meshsat/meshsat-fieldkit/v2/docs/records/README.md

# Session records cited by the committed pages

MESHSAT-1357, filed 26 September 2026 (stream `records`, from main `45bde541`). The MeshSat field kit V2 is a prototype design: no board of the set has been built, and nothing in this folder has been measured on hardware.

## What this folder is

The foundation session of 25 and 26 September 2026 worked in git worktrees, one per stream (branches `fnd/<name>`), and kept its working files in each worktree's untracked `drafts/` folder: the scripts it ran, their outputs, the netlist readings, the decision logs of each board's author and the lists of documents it fetched. Committed pages cite those files, and no reader of the repository could open them. They are filed here so an outside reviewer can.

- **Layout.** `v2/docs/records/<worktree>/<the same path below drafts/>`: `drafts/dec_loop.py` of worktree `fnd/rv-dec` is `rv-dec/dec_loop.py` here.
- **Records, not repository tools.** No test, gate or generator runs them. A script here keeps its original text, including paths into `drafts/` or onto the rented build box (`/root/...`) that only existed where it ran; the table below maps every such `drafts/` path to its place here.
- **Byte for byte**, with two exceptions: in `rv-dec/PCB-OPEN-PAIRS.decision-42.isolated.diff` and `r4b/box/r6-run6/check_pcb_b/emul-r6-gate-on-round6.txt` the absolute path of the session's scratch directory on the build host is replaced by `$SP` (the notation `MESHSAT-709-geometry-appendix.md` already uses for it). The table gives the filed sha256, and the section *Rewritten on filing* gives the worktree file's.
- **Not filed here** (sections below): maker documents, which belong in `v2/vendor/` with the parts stream; netlists and box run directories that are over 1 MB or that the repository's history already holds, each with its sha256 and the command that rebuilds it; third-party web page snapshots the battery packet chose not to publish. Nothing filed holds a credential or personal data; the only mail addresses in the folder are two companies' published functional ones (AsiaRF's sales address in `rv-pwr/pwr-maker-questions.md`, Jauch's battery-technology address quoted from its web page in `rv-bat/datasheets/SOURCES.txt`).
- **The session's choices in this filing** (taken by the session under the owner's standing rule of 26 September 2026): a file whose bytes the repository already holds is not filed twice, it is pointed to; a netlist that differs from a committed one only in its `(source ...)` and `(date ...)` header lines is rebuilt by a command whose output hash is checked here, not filed; the outputs of the scripts `DECOUPLING.md` section 11 cites are filed with them, because that page cites the scripts "and their outputs"; the two box scripts that `r4b/box/r6-run6/README.txt` names as the run's driver are filed with it.
- **A decision log is filed whole**, as its worktree held it when this was filed. `r4t/r4-decisions.md` is a snapshot of a file another loop was still editing (worktree file modified 20:50 CEST); see *Cited but not found*.

Worktrees:

| folder | whose records |
|---|---|
| `adj/` | the eleven adjudications A01 to A11 of 25 September (filed 27 September; section *Filed 27 September 2026*) |
| `handover/` | filed by the handover's H1.1 editor, 27 September 2026, so the handover pages' citations can be traced: hc4's two reviews and hc6's review, rendered from the session's workflow journal (AI reviews); the messages of commits `3a1f6576` (the parity report of 36 artefacts) and `a8652172` (the H1 filing, with the suite results); `3a1f6576-commit-message.txt` sha256 382d1771c084903b; `a8652172-commit-message.txt` sha256 15d4f2b04fd46883; `hc4-reviews.md` sha256 6941573f2b81298b; `hc6-review.md` sha256 3a72258e350d3ad7 Added 27 September 2026 by the integrating session: `H2-USABILITY-CHECK.md` (sha256 `b7e555783614defb1ce572a54786f11d6d93cc7ead7b52ec426557ddfd069fbe`), the fresh checker's full result on snapshot H2, filed verbatim from the workflow journal (AI usability check); `RELEASE-H2.md` in `v2/docs/handover/` cites it. |
| `hc2/` | the layer 2 closer hc2 (concept of operations, envelope and test plan) and its targeted fixer c23: the power and heat arithmetic the pages cite and the closer's hand-offs (filed at integration, 27 September 2026) |
| `hc3/` | the layer 3 closer hc3 (requirements registry) and its targeted fixer c23: the hand re-read of every carried citation, the list the apply script checks, the fixer's answer to each finding, and the layer's open questions and status row (filed at integration, 27 September 2026) |
| `hc4/` | the layer 4 closer hc4 (readable diagrams): the five disagreements between the energy chain and the netlists, for the energy chain's owner (filed at integration, 27 September 2026) |
| `hc7/` | the layer 7 closer hc7 (case fit and the case release) and its targeted fixer c7: board C's gate readings with and without the board reading, the fixer's answer and the landing notes (filed at integration, 27 September 2026) |
| `r4a/` | board A's author, rounds 4 to 6 (round-6 candidate, fix-ups 3 and 4) |
| `r4b/` | board B's author, rounds 4 to 6 (round-6 candidate, box run 6) |
| `r4e/` | board E's author, round 4 |
| `r4p/` | board P's author, round 4 |
| `r4t/` | the shared tools' author, rounds 4 to 7 (still being edited when this was filed) |
| `r6d/` | board D's author, round 6 |
| `r8b/` | board B's author, round 8 (the round's decision record, its tools, evidence and per-finding change list, and the decoupling classes; filed at integration, 27 September 2026, `drafts/b/X` at `r8b/X`); `r8b/integration/` holds the integration's own box procedure, comparator and logs |
| `r8d/` | board D's author, round 8 (the regeneration's independent comparison, gates and suite; filed at integration, 27 September 2026) |
| `r8int4/` | the integrator of set 4 of the handover (27 September 2026, branch `fnd/r8int4`): the scripts that merged the layer 2 and 3 closers, the re-take driver, the hardware-firmware contract and the case release onto main `38dcd764`, the hand re-reads they needed and the apply logs |
| `r8int5/` | the integrator of set 5 of the handover (27 September 2026, branch `fnd/r8int5`, on main `953f5658`): the shared helpers its per-stream scripts use (`edlib.py`, `render_group1.py`, `file_stream.py`; `file_records.py` is `r8int4/file_records.py` byte for byte and is not filed twice), the CURRENT-EVIDENCE rebind, the final regeneration of boards A, B, D and E on the KiCad box (`final-regen/`: every artefact PARITY or PARITY_AFTER_NOISE, the sidecars' generator identities unchanged) and its logs; each stream's own scripts are in its folder (`w3t/`, `w3a/`, `w3b/`, `w3de/`, `w3g/`); the session scratch path is written $SP in `file_stream.py`, `logs/diagrams-readback-b7f96784.log`, `logs/tests-w3de-targeted.log` |
| `r8int6/` | the integrator of set 6 of the handover (27 September 2026, branch `fnd/r8int6`, on main `6ec37197`): the shared scripts that applied streams w4r, w4b, w4c, w4ae and w4dp (`common/` and the drivers; each stream's own apply script is in its folder), the set 6 lines on the layer status page with the V2-SPEC correction and the open item they name (`layers_r8int6.py`), the CURRENT-EVIDENCE rebind, the final regeneration of boards A, B, C, D, E and P on the KiCad box at `932cf9d7` (`final-regen/`: every artefact PARITY or PARITY_AFTER_NOISE, no land moved, every sidecar's generator identity equal to the committed one, so no sidecar is re-stamped), the independent netlist comparison of each board against its stream's expected list (`indep/`), and the evidence phase's logs (`evidence-phase/`); the session scratch path is written $SP in `commit_r8int6.sh`, `common/file_stream_r8int6.py`, `copy_evidence.sh`, `evidence_r8int6.sh`, `indep/summary.txt`, `kitprep_r8int6.sh`, `stream_r8int6.sh`, `validate.sh` |
| `r8p/` | board P's author, round 8 (the regeneration's independent comparison and the second pass against the first, and the JLC record of F1's holder; filed at integration, 27 September 2026). Board P's generator names `drafts/p/` at `gen_sch_p.py:587` and `:598`: the stream's battery-packet drafts, landed in `v2/docs/review-packets/battery/` by the same commit |
| `rel2/` | the second release attempt of layers 1 to 3 (27 September 2026, branch `fnd/rel2` from `953f5658`): the registry's apply script, the documents' and the handover's edit scripts, the rebinds with their asserted byte-identities, and the tool-compatibility evidence for the requirements validator's change; authored in the tree, not filed from drafts |
| `rel2f/` | the release finalizer of layers 1 to 3 (27 September 2026, branch `fnd/rel2` rebased onto `391d8579` and then `91894cd7`): the rebase's resolver and its line-by-line check, the third tool entry of COMPATIBILITY.md, the rebinds of the two readings bound to CURRENT-EVIDENCE.md, the registry's apply script for the items the second release check left, the documents' edit script, the needs pin and the CONOPS rebinds, and the ids they took; authored in the tree, not filed from drafts |
| `h2/` | the targeted fix of layers 1 and 3 (27 September 2026, branch `fnd/h2` from `62f26a44`): the registry's difference from the file layer 3's second release check read, computed entry by entry, and the script that writes the baseline and closes S-51, S-77 and S-78; and its finalizer's script after the narrow verification (the baseline reversed, S-51 and S-78 reopened, S-80 added); the H2 assembler's count script with its output, and in `h2/box/` the scripts and logs of its KiCad box runs (the exports, the regeneration, the ZIP route of REGENERATE.md); authored in the tree, not filed from drafts |
| `energy/` | stream energy (28 September 2026, branch `fnd/energy` from `038037ed`): mission M1's energy reconciliation on the owner's instruction of that day, M1 and REQ-072 preserved as written: the loads of each state with their kinds, the usable pack energy, the night at 52 N by month, the solar input per day, the hour-by-hour balance with its sensitivity, the options ranked and the smallest justified changes for the owner's decision (`ENERGY-RECONCILIATION.md`, `DECISION-PARAGRAPH.md`, `energy_budget.py` with its pinned inputs and output); authored in the tree, not filed from drafts |
| `a1solar/` | stream a1solar (29 September 2026, branch `fnd/a1solar`, second issue after its AI check): Option A(i)'s solar panel selected from makers' documents (six candidates; the design basis four Renogy RNG-100DB-H in 2S2P, a session decision gated on the owner's REQ-016), the array's cold Voc, hot and edge-of-cloud Isc, the stage's 34.3 V fixed input point, the entry at 20 A and 56.3 V, REQ-016 per arrangement for the owner, a gated draft list for board E's writer, both energy design cases at the array's typical and adverse ratios, and the planes the array may face from 50 PVGIS mean days (`SELECTION.md`, `ARRAY.md`, `array_calc.py`, `energy_runs.py` with their outputs); authored in the tree |
| `csi/` | stream csi (29 September 2026, branch `fnd/csi`, three rounds, checked three times): board C's SI-001 nets decided, allowed pending the layout, or open; the allowance method tied to its reference nets; the e-paper series resistors R53 to R56 (`apply/`), applied in set 13 |
| `walkmin/` | the walk minors (29 September 2026, branch `fnd/walkmin`, checked): RF-002's walk takes an EMCON toggle only on its declared contact lugs, and the board key is required |
| `int16/` | integration set 15 (29 and 30 September 2026, branch `fnd/int16`): PANJIT's SS2020FL sheet held back, w5identc and s122 merged, S-122 closed by its filed check 8 (CFL-016 PASS), the set's integration check and its fixes (`checks/`, README) |
| `w5identc/` | stream w5identc (29 September 2026, branch `fnd/w5identc`, four rounds, checked three times: `checks/`): board C's part identities, 21 printed, 23 decoded under decision 59, 41 unresolved with reasons |
| `int15/` | integration set 14 (29 September 2026, branch `fnd/int15`): s120 and s122 merged, their registry scripts run, S-122's closure withdrawn as premature and its closing script gated on a part-number finder and the corrected rows, the substance left to the filed check, the checks |
| `int14/` | integration set 13 (29 September 2026, branch `fnd/int14`): s119, csi and walkmin merged, board C regenerated and read back, the pins, sheets, rebinds and checks |
| `s120/` | stream s120 (29 September 2026, branch `fnd/s120`, four rounds, checked four times: `checks/`): board A's charge bus VBUS20 bounded at 23.40 V (INFERRED, the front end's typical 10 percent over-voltage trip) against the 30 V charger FETs of decision 57; S-120 closed and S-124 opened for the switch nodes, closed only on the prototype |
| `s122/` | stream s122 (29 and 30 September 2026, branches `fnd/s122`, `fnd/s122b` and `fnd/s122c`, eight rounds, checked eight times, closed by check 8: `checks/`): the documents CFL-016 names re-read against the netlists by an inventory and verdict script, the stale sentences its inventory found corrected, CONOPS restored to its baseline text with its current values on the status page; S-122 open until part numbers are inventoried and five more sentences corrected (set 14's checks) |
| `s119/` | stream s119 (29 September 2026, branch `fnd/s119` from `a1f8ec70`, S-119, two rounds): the energy chain's charger rows restated from the FETs' losses (U3 0.98 to 0.979 with decision 57's FETs; U3B 0.975 to 0.972 on U3's 400 kHz row, the session decision drafted by `apply_decision_s119.py`, weighted over the model's own hours by `u3b_hourly.py`), U3B's inductor checked (`inductor_u3b.py`), the chain's scripts re-issued with their pins moved and every output regenerated, the headline figures before and after (`headline_diff.py`), Option A(i)'s lid reconciliation re-run with the change from the accepted figures, U3B hour by hour, the failing case, the sensitivity, the room for the excluded core loss and the deployment rule's planes (`reconcile_s119.py`), the parsed comparison that re-pinned energy_4s6p.py's gen_sch_a.py (`cmp_gen_sch_a.py`), and the apply scripts for the registry, the decision register and the pages; authored in the tree |
| `l3am/` | the layer 3 amendment (1 October 2026, branch `fnd/l3am` from main `b45d1705`): the independent review the owner relayed, filed byte for byte, and its findings' dispositions (`DISPOSITIONS.md`); the solar-assisted figures labelled as proposal P-03's (L3-R01, with the understated shortfall carried from the layer 4 check), REQ-042's acceptance an end-to-end verification (L3-R02), the acceptance bound to the reviewed content (L3-R04) and REQ-016's protection judged apart from its window (L3-R05); the scripts that apply them, the run order and the coordinator's re-acceptance (`README.md`) |
| `l3r5/` | layer 3's round 5 and its closure (30 September 2026, branch `fnd/l3r5` from `fnd/l3r4` `a547fe1d`, on the owner's reviewer's review of the decision brief, D-26, the owner's addendum on M1's runtime, D-27, and his clarifications D-28 to D-31, applied by `apply_l3r5_closure.py`): the scripts that record D-26 to D-31 (`apply_l3r5_d26.py`, `apply_l3r5_d27.py`, `apply_l3r5_d28_d29.py`, `apply_l3r5_d30.py`, `apply_l3r5_d31.py`), the closure and its layer status script (`apply_layer_status_l3_r5b.py`), the one that brings `LAYER-STATUS.md`'s layer 3 to the new semantics, the gate's fifth condition and the status levels (`apply_layer_status_l3_r5.py`), and the two checks of streams l3feas and l3batt filed byte for byte (`checks/`), the reader and fill of row L3-OD7's table (`runtime_reader.py`, `fill_l3r7_from_comparison.py`), and the fix round on the engineering collaborator's closure check (`checks/astra-check-l3r5-1.md`, filed byte for byte; `apply_l3r5_supersede_sc21.py`, `apply_l3r5_d38.py`, `apply_definition_status_l3r5.py`, `apply_layer_status_l3_r5c.py`); the records themselves are `l3feas/` and `l3batt/`; `README.md` has the run order |
| `l3batt/` | stream l3batt's bounded runtime and battery comparison (30 September 2026, branch `fnd/l3batt` at `63897fc3`, accepted by its CHECK-3, its three checks filed in `l3r5/checks/`): the provenance of M1's 72 hours (`PROVENANCE.md`), options A (48 hours required, 72 desired) and B (72 hours required) with HF and the tablet kept (`COMPARISON.md`, `runtime.py` and `runtime.out`), the load traced (`load_trace.py`), the lid in 21700 cells (`lid_21700.py`) and a battery shortlist (`SHORTLIST.md`, `fetch_held_back.py` for the sheets held back by their terms) and the lid tablet's USB-C service budget, a proposal (`TABLET-BUDGET.md`, `tablet.py`, `tablet.out`), filed byte for byte and bound by `l3r2.yaml` `runtime_comparison`; row L3-OD7 is filled from it |
| `l3feas/` | stream l3feas's bounded feasibility record (30 September 2026, branch `fnd/l3feas` at `c11b99d3`, accepted by its CHECK-2, filed in `l3r5/checks/`): the kit-level pass line's exact reference case, HF kept with WAB (`hf_wab.py`) and the solar interface quantity by quantity with its obligations (`solar_interface.py`), filed byte for byte and bound by `l3r2.yaml` `feasibility_basis` |
| `l3r4/` | layer 3's round 4 (30 September 2026, branch `fnd/l3r4` from `8fec0733`, preparation while the owner's six answers are pending): the generator of the definition re-issue, closure item L3-C26 (`reissue.py`: the CONOPS and product brief passages each answer changes, mapped in `PASSAGE-MAP.md`, and the draft and change record it writes once the answers are recorded), and the script that brings `LAYER-STATUS.md`'s independent-check row current (`apply_layer_status_l3_r4.py`); `README.md` has the run order |
| `l3r2/` | layer 3's second issue, L3-R2 (30 September 2026, branch `fnd/l3r2` on `4012429e`, on the owner's instruction D-21, his review D-22, his instruction on the six-row table D-23, his addendum on the power path D-24 and his corrections D-25): the registry's editing helpers (`l3edit.py`), the session's closures (`apply_l3r2_session.py`, `apply_l3r2_d23.py` to `apply_l3r2_d25.py`, `apply_l3r2_r3b.py`), the basis reader and the prepared fill (`basis_reader.py`, `set_energy_basis.py`, `fill_l3r2_from_basis.py`), CFL-006's re-read (`read_cfl006.py`), the layer status page's layer 3 restated (`apply_layer_status_l3.py`, rounds 3 and 3b `apply_layer_status_l3_r3.py` and `apply_layer_status_l3_r3b.py`), the prepared owner-decision scripts of rows L3-OD1 to L3-OD6 (`conditional/`, not applied, rows 1, 2, 4 and 6 held until the energy basis and the power path are checked) and their dry runs (`dryrun.py`), the independent checks of L3-R2 and the checks of the energy basis (`checks/`); the pages are `v2/docs/handover/layer3/`; authored in the tree |
| `scrub/` | the public-file scrub (30 September 2026, branch `fnd/scrub` from `8fec0733`, on the owner's instruction of 29 September 2026): the runner's paths, session scratch paths and host names replaced by neutral tokens or derived in 57 files, the files left with the reason, the four snapshots reissued as H1-R1, H1.1-R1, H2-R1 and H3-R1 beside the ones they supersede, the guard `test_public_hygiene.py`, and `MAP.md`, every replacement by file, line and token class; history not rewritten |
| `l3rb/` | the re-baseline of layer 3 (27 September 2026, branch `fnd/l3rb` from `ef144760`): the script that applies S-80's wording fix exactly as the narrow verification of the targeted fix gives it and records its observation (c) as S-81, the script that writes the baseline at `a54b793b` and closes S-51, S-78 and S-80, and the registry's entry-by-entry difference across both; and, after the re-check of those two commits (`v2/docs/reviews/TARGETED-RECHECK-LAYER-3-2026-09-27.md`, B-1 CLOSED), the script that files it in the registry with its asserted output and the script that edits the handover pages; authored in the tree, not filed from drafts |
| `h2m/` | the H2 minor-findings editor (27 September 2026, branch `fnd/h2m` from `ef144760`), answering the H2 usability check's fourteen minor findings (`v2/docs/handover/H2-RESPONSE.md`): the script that gave LAYER-STATUS.md its acceptance tables at H2 and moved each layer's audit into its Appendix A (its bold status format was corrected by hand after the run), and in `h2m/box/` the script, log and result of REGENERATE.md section 9's third route on the rented KiCad box: a repository built from `H2.zip` with `handover_pack.py repo` as committed on main in `a54b1f4d` (first cited as `992f2bc2`, the same patch on the branch before it was re-integrated), section 1a's fetch with the computed `REF`, and board P's re-take; authored in the tree, filed byte for byte |
| `h3/` | the H3 pages worker (27 September 2026, branch `fnd/h3` from `6ec37197`), preparing the source commit of handover H3 by corrections to pages only: the count script of the H3 pages and its output; the difference from H2's source commit `b89b50b4` by class, which asserts that no design file, generator or checking tool changed and that the registry differs from its baseline `a54b793b` in no protected field; the public check of the commits the pages name; the patch ids of the commits `H2-RESPONSE.md` first cited against main's; the estimate of the ZIP's size before the build; the check that no edited page is bound by the registry, with the rebind path and its self-test; and this index's own apply script; authored in the tree, filed byte for byte |
| `rv-bat/` | review stream BAT, the battery and protection review packet |
| `rv-dec/` | review stream DEC, decision 42 (decoupling placement) |
| `rv-emc/` | review stream EMC, the per-transmitter EMCON table |
| `rv-pwr/` | review stream PWR, the power and thermal budget |
| `rv-zer/` | review stream ZER, the ZEROIZE key and slot lifecycle |
| `ts-net/` | the tools stream ts-net (PWR-001 and SI-001 on the netlist), rounds 7 and 8 (its session decisions; filed at integration, 27 September 2026) |
| `w1/` | foundation workstream 1 (systems and requirements): the owner decision table, the conflict list and the candidate requirements, 25 September (filed 27 September) |
| `w2/` | foundation workstream 2 (power and runtime), 25 September |
| `w3a/` | board A stream w3a (EQ-17, EQ-19 for A, the PoE and USB-C enable dividers, EN9V), filed at the r8int5 integration of 27 September 2026: its drafts as the stream left them after its second pass, its parity instrument and box readings, and the integrator's re-derived scripts (`*_r8int5.py`, the independent checks' corrections applied) that ran on main 953f5658; the session scratch path is written $SP in `readings/tests-targeted.txt`, `readings/before/derate.verdict.json` |
| `w3b/` | board B stream w3b (EQ-19 for B, decision 42's classes in the generator, W3B-F1, W3B-F2, W3B-R1), filed at the r8int5 integration of 27 September 2026 (board B's generator cites this folder): its decision record, box drivers, parity comparisons against `expected_w3b.json` and readings, and the integrator's re-derived scripts; the Slkor BC857B sheet is filed once, at `v2/vendor/slkor/`, not here. The independent check's notes not applied in the files: `w3b-decisions.md` and gen_sch_b.py cite the STM32H743's VCORE maximum as Table 123, which is Table 122 on p.212; the session scratch path is written $SP in `evidence/gates-after/clock_check.verdict.json`, `evidence/gates-after/derate.verdict.json`, `evidence/gates-after/pin_map_lands_b.verdict.json`, `evidence/gates-after/review_nets.log`, `evidence/gates-before/clock_check.verdict.json`, `evidence/gates-before/derate.verdict.json`, `evidence/gates-before/pin_map_lands_b.verdict.json`, `evidence/gates-before/review_nets.log` |
| `w3de/` | board D and E stream w3de (EQ-19 for D and E, S-47's bottom-leg sense, EQ-16's dock decision and board A's half of it), filed at the r8int5 integration of 27 September 2026 (the registry, the interface contract and board A's generator cite this folder): the decision record and its arithmetic (`EQ16-dock-vin-raw.md`, `dock_contacts.py`), the drafted patches as the stream left them, its parity instrument and expected-change lists, and the integrator's re-derived scripts with board A's regeneration on its w3a generator (`parity-r8int5/`); `a-half/` (board A's files regenerated on main's generator, superseded by that regeneration) is not filed. `patch_test_rails_census.py` was not applied: board A stream w3a's patch makes the same change in the shared replay helper. Not filed, because the repository holds the same bytes (the regeneration's outputs are board A's committed files at the w3de commit, and `committed/` holds the w3a commit's) or they are the box's ERC reports: `w3de/parity-r8int5/regen-out-a/a/regen-pcb-a-power.kicad_sch` sha256 54b24eb100332ed5; `w3de/parity-r8int5/regen-out-a/a/regen-pcb-a-power.net` sha256 da05dc02bc1e612f; `w3de/parity-r8int5/regen-out-a/a/regen-pcb-a-power-intent.json` sha256 92dd3b1cda9046b8; `w3de/parity-r8int5/regen-out-a/a/regen-pcb-a-power.net.prov.json` sha256 d8d7731057a92b79; `w3de/parity-r8int5/regen-out-a/a/regen-pcb-a-power-erc.json` sha256 ac8c6bd0147d607d; `w3de/parity-r8int5/regen-out-a/a/committed/pcb-a-power.kicad_sch` sha256 3c34f26af02efbb2; `w3de/parity-r8int5/regen-out-a/a/committed/pcb-a-power.net` sha256 c57d119d21f45fe9; `w3de/parity-r8int5/regen-out-a/a/committed/pcb-a-power-intent.json` sha256 2e686478fb0edeef; `w3de/parity-r8int5/regen-out-a/a/committed/pcb-a-power.net.prov.json` sha256 b22848e7d502b694; `w3de/parity-r8int5/regen-out-a/a/committed/pcb-a-power-erc.json` sha256 bfff2b36a9dff7ad; |
| `w3g/` | the layer 4 stream w3g (the diagrams rebuilt on round 8 at 38dcd764), filed at the r8int5 integration of 27 September 2026: its drafts (the handover label script the integration ran, the board E FET-symbol finding for board E's author) and the integrator's scripts that brought its files onto set 5's netlists (`*_r8int5.py`, the ARCHITECTURE.md reference-line diff they re-applied) |
| `w3t/` | the tools stream w3t (EQ-18, the SN74LVC1G57 row of the RF-002 walk) and its finding W3T-F1, filed at the r8int5 integration of 27 September 2026; `w3t-decisions.md` and `HANDOFF.md` carry the independent check's corrections (marked 'corrected at integration'), and `apply_registry.py` is the copy that ran (both files computed before either is written, the W3T-F1 wording corrected) |
| `w4/` | foundation workstream 4 (mechanical, thermal and RF), 25 September |
| `w4ae/` | boards A and E stream w4ae (HOT-R1 drawn: board E's Q11 open drain on BLK_SPARE driven by the sensor controller's GPIO19, board A's R216 pull-up on DOCK_SPARE; board E's fan flyback diodes D7 and D8 given their order code and sheet), filed at the r8int6 integration of 27 September 2026 (the registry binds `hot_r1_trace.py` here; the registry, CONOPS, HW-FW-CONTRACT and EQ-22 cite this folder): its README (with the ids taken at integration appended), the registry and document drafts, the H2 path trace with its readings, the regeneration's parity records, the JLC and LCSC answers, `ids.json` as its registry script wrote it, and the integrator's re-derived scripts (`*_r8int6.*`: the independent check's corrections); the Zhengxin sheet is filed at `v2/vendor/zhengxin/`; the session scratch path is written $SP in `readings/tests-final.log` |
| `w4b/` | board B stream w4b (RF-002 under D-05: the RockBLOCK's ENABLE forced low by EMCON, L4 case (2) on the switch enables, the card bucks' enables on each slot's own 5 V), filed at the r8int6 integration of 27 September 2026 (board B's generator, EMCON.md section 4c and the registry cite this folder): its decision record (with the ids taken at integration appended), the drafts it asked the integrator to apply (the RF-002 walk's rows and their tests, check_pcb_b's EMCON block, the page drafts, the registry script), its expected-change list, box driver, evidence and readings, and the integrator's re-derived scripts (`*_r8int6.*`: the rows landed with the board change, the independent check's corrections); the two maker documents are filed at `v2/vendor/ti/` and `v2/vendor/rockblock/`, not here |
| `w4c/` | board C stream w4c (EQ-25 option (a): R14 2.2k and R50 10k so TX_INHIBIT_n fails safe with the panel unpowered; PWR-001's declarations on board C with +3V3 covering EPD_VCC; W4C-F1, the RAIL_SENSE divider), filed at the r8int6 integration of 27 September 2026 (the registry, EMCON.md, PANEL.md and ENGINEERING-QUESTIONS.md cite this folder): its decision record and README (with the ids taken at integration appended), the registry and document drafts, the regeneration's parity records and every scratch reading before and after, and the integrator's re-derived scripts (`*_r8int6.*`); the UC8253c sheet is filed at `v2/vendor/pdi/`, not here |
| `w4dp/` | boards D and P stream w4dp (board D's flyback diode D2 ordered with its maker's sheet; board P's supplies declared for PWR-001 with the fuse gate bounded by TI's 6 V drive; BAT-001's table pcb_pack_protection.yaml brought to the drawn circuit and its hardware level judged against the cell maker's limits), filed at the r8int6 integration of 27 September 2026 (the registry, the coverage notes and TEST-PLAN.md cite this folder): its README (the stream's record, with the independent check's derate correction and the ids taken at integration appended), the registry, coverage, TEST-PLAN and vendor-index drafts, the regeneration's parity records for both passes, every scratch reading and the projection, and the integrator's re-derived scripts (`*_r8int6.*`) with the `ids.json` they wrote; the 1N4148W sheet is filed at `v2/vendor/power/` |
| `w4r/` | stream w4r (board E5's INT-001 decided by its own dock contract reading, block_contract.py judging E5 against board A's current netlist), filed at the r8int6 integration of 27 September 2026: its drafts as the stream left them (the rules_status, re-take driver, coverage, render and registry patches, all applied at integration), its scratch readings on the KiCad box, and the integrator's apply script with the two corrections of the independent check (`*_r8int6.*`) |
| `w6/` | foundation workstream 6 (findings review), 25 September |
| `hc5/` | the layer 5 closer (27 September): the kit I2C bus budget, its script and two outputs, the interface contracts' field check with its output, and the USB 2.0 clauses it cites; authored in the tree, not filed from drafts |
| `w5/` | foundation workstream 5 (the hardware and firmware contract, round 2), 26 September |
| `defstab/` | the definition-baseline restructure of `PRODUCT-BRIEF.md` and `CONOPS.md` (27 September 2026, branch `fnd/defstab` from `31cd29b9`, commit `fa89c7c6`; the independent review of handover H2, section 4): the map of every move and the scripts that wrote, asserted and re-derived it, and the registry's apply script (section *Filed 27 September 2026: the definition restructure's map*) |
| `retake6/` | the consolidated re-take of set 6 (27 and 28 September 2026): the box scripts and readings (`box/`, `RESULT.txt`), the analysis of what moved, and the script that rebinds CON-010 and REQ-044 to the re-rendered evidence page |
| `int7/` | integration set 6 (28 September 2026, branch `fnd/int7`): the registry merge resolver, CON-010 re-decided from the readings by a predicate, the waits_on dispositions, the answers to the three AI checks (`CHECK.md`, `CHECK-2.md`, `CHECK-3.md`, `CHECK-RESPONSE.md`), the closure record and the page rebind |
| `w5si/` | stream w5si's record (27 September 2026), filed at set 7: its edges check, its readings and tools, and its recovery after the runner's reboot; the makers' IBIS models it used are never committed |
| `w5si2/` | stream w5si2 (28 September 2026, branch `fnd/w5si2`): SI-001's edge rates made integrable without publishing a model, and board C's declarations, with readings and tools |
| `w5tray/` | stream w5tray (28 September 2026): the QMX lid tray r2 (S-63, EQ-24), its passes, drafts and recovery record; AI work and AI review only |
| `d8dec31/` | stream d8dec31 (28 September 2026): what the AI review of decision 31 (`v2/docs/reviews/DECISION-31-PROTECTION-TOPOLOGY.md`) was written from, its declaration, registry, hold and generator apply scripts, and the pin tables it read |
| `d6rel/` | stream d6rel (28 September 2026, finding H3-01): REL-001's population read on an explicit inventory, the four-case matrix before and after the tool's repair, and its apply scripts |
| `p3bind/` | stream p3bind (28 September 2026): the layout constraint sheets bound to their inputs, the rail commits and moves behind each sheet, and the rule and coverage apply script |
| `cx1/` | the Codex pilot on finding I-03 (28 September 2026, branch `fnd/cx1`; an AI worker of a second model family): the A to B power leads reconciled against the makers' pages (`ANALYSIS.md`, its correction `CORRECTION.md`, `if_ab_power.py` with its output), the declarations draft, and the independent Claude checks under `checks/` |
| `int8/` | integration set 7 (28 September 2026, branch `fnd/int8`): the apply scripts of the carried check items, the owner's rulings of that day (D-19, D-20, S-114), the I-03 items and the contact rating, the AI check and the closure record |
| `s99/` | S-99, board A's +5V_DEV stage against the coincident demand (28 September 2026): the analysis, the Codex correction with its checks, the rail-by-rail actionable list (`RAILS-ACTIONABLE.md`), `dev_stage.py` and the D8 split draft |
| `s98/` | stream s98 (28 September 2026): the interim alignment of the A to B power declarations, the contract and architecture apply scripts, the box regeneration of boards A and B, the lead ends, the closure text and the layer rows |
| `int9/` | integration set 8 (28 and 29 September 2026, branch `fnd/int9`): S-98 closed for declaration consistency, the rebinds after the regeneration of boards A and B proved by AST and by parsed netlists, the netlist pins moved, the constraint sheets re-bound, and the box records |
| `s99a/` | stream s99a (28 and 29 September 2026): S-99's corrected D8 split applied to board A's generator (decision 55): U41's divider arithmetic, the parsed comparison, the codec-floor and layout open items, the registry draft and the tests |
| `od01/` | the OD-01 case package for the owner (28 September 2026): the checkout list, the machining request, the operator's test brief, and the two AI checks under `checks/`; purchasing stays with the owner |
| `int10/` | integration set 9 (29 September 2026, branch `fnd/int10`): the regeneration of board A with S-99's D8 split, the pins moved on a parsed proof, sheet A re-bound, the judged rebind of the records bound to board A's netlist and generator, stream s99reg's scripts for S-99's registry texts, decision 55, the interface rows and the pages (with its dry run and the erratum to the decision 31 review), the records index, the page rebind, and the box records |
| `d6dec/` | stream d6dec (28 and 29 September 2026): decision 42's decoupling tools T1 to T6, T9 and T10 (the class rules, the fan selection, the escape cost), DEC-001's registry apply script (T7), the basis check of every declaration's quotation against the held PDFs (BASIS.md), the inventory, the box records and the log |
| `diag/` | the rebuild of the eleven diagrams after sets 6 to 9 (29 September 2026, branch `fnd/diag`): the readback's output (every SVG readable and labelled, every PDF at its drawing's size) |
| `int11/` | integration set 10 (29 September 2026, branch `fnd/int11`): streams d6dec, energy (section 9) and diag; DEC-001's registry text; set 9's carried items M2, M10 and M11 (S-117); the regeneration of all six schematics after the decoupling tools entered every generator's import closure, with the pins, records and sheets re-bound on proofs of identity; two re-takes; the page rebind; the closure record |

## Filed files

Paths are relative to this folder; the source is the same path below `drafts/` in the worktree named. sha256 is of the file as filed.

| file | sha256 | bytes | source worktree and path | cited by |
|---|---|---:|---|---|
| `hc2/LAYER-STATUS-layer2.md` | `e9afbcd47112a10619abab33c8378fceeeab05dbe726f740b59ac46213cf3729` | 8272 | `fnd/hc2` `drafts/LAYER-STATUS-layer2.md` | `v2/docs/handover/LAYER-STATUS.md` (layer 2) |
| `hc2/handoffs.md` | `60bfcc5f205a09fc23eb249a0aa012c30da38cbec6d4c4d9333253916be53943` | 29166 | `fnd/hc2` `drafts/handoffs.md` | `v2/docs/handover/LAYER-STATUS.md` (layer 2) |
| `hc2/hotstop_bounds.out` | `5f03619f7bf5c476e57f90ef17e161989ceac6e9b0df8b40b25d60ed5dfdf825` | 8163 | `fnd/hc2` `drafts/hotstop_bounds.out` | `v2/docs/CONOPS.md`<br>`v2/docs/OPERATING-ENVELOPE.md`<br>`v2/ecad/tools/pcb_envelope.yaml`<br>`v2/ecad/tools/pcb_requirements.yaml` |
| `hc2/hotstop_bounds.py` | `ed8f8c6b4c3bed083883439ccfb9fc1a96bb4c3864fc4dc3bc3f934beb1dcf8f` | 8097 | `fnd/hc2` `drafts/hotstop_bounds.py` | `v2/docs/CONOPS.md` (section 4c) |
| `hc2/pwr_red2.out` | `835910e807d588c481951dc879e030b55d893453bd124872b9310a99bed46db6` | 13896 | `fnd/hc2` `drafts/pwr_red2.out` | `v2/docs/CONOPS.md`<br>`v2/docs/OPERATING-ENVELOPE.md`<br>`v2/ecad/tools/pcb_envelope.yaml` |
| `hc2/pwr_red2.py` | `5790bc7e444bebc4b6b7b6616c4641dfe602185631992d19aeb223eb51e9feec` | 12629 | `fnd/hc2` `drafts/pwr_red2.py` | `v2/docs/CONOPS.md`<br>`v2/docs/OPERATING-ENVELOPE.md` |
| `hc2/sc.md` | `83cca82cce9d4c43ff5f238a61d2bb4ee0338e600237a3d2cc0ab85ad1f6f055` | 20465 | `fnd/hc2` `drafts/sc.md` | the layer 2 closer's session choices, numbered in `v2/ecad/tools/pcb_requirements.yaml` |
| `hc3/apply_registry.py` | `009770cb4413f14acbb235cbcf92a897288bba85cdd84e46d9d1abb8134a38de` | 362929 | `fnd/hc3` `drafts/hc3/apply_registry.py` (generated from the `ops_*.py` beside it in that worktree) | the registry change of this integration, by record id |
| `hc3/blocked-questions-layer-3.md` | `c6a8d3693cc962b6f28daa75f05f04c3c1778af276c6cc68fd07194bab992491` | 21559 | `fnd/hc3` `drafts/hc3/blocked-questions-layer-3.md` | `v2/docs/handover/ENGINEERING-QUESTIONS.md`<br>`v2/docs/handover/LAYER-STATUS.md` (layer 3) |
| `hc3/c23-response.md` | `add69d02b8232a6b11514938f203a47d7de32d8cdc564c8c705d94543b569509` | 22303 | `fnd/hc3` `drafts/c23-response.md` (the same bytes as `fnd/hc2` `drafts/c23-response.md`) | `v2/docs/handover/LAYER-STATUS.md` (layers 2 and 3) |
| `hc3/citations-reread.md` | `62bbcc4c84e5ec30be51712da5bf08567c75d572ab0a39c79cb61724ba44afdc` | 17762 | `fnd/hc3` `drafts/hc3/citations-reread.md` | `v2/ecad/tools/pcb_requirements.yaml` (header comment) |
| `hc3/layer-status-layer-3.md` | `9a2d72a87446eced17899dd80a80943874a85b0ad4f573bdb3fc43c76c03c89e` | 4942 | `fnd/hc3` `drafts/hc3/layer-status-layer-3.md` | `v2/docs/handover/LAYER-STATUS.md` (layer 3) |
| `hc3/reviewed-citations.json` | `4b4e4031bf44ef9770c147286150d4f7358a2daa42b7ed9ec276b19c5dce93e4` | 7826 | `fnd/hc3` `drafts/hc3/reviewed-citations.json` | the apply script's citation guard (`citations-reread.md`) |
| `hc3/reviewed-pairs.json` | `6275e1cdc16a026eec30e39992dbcfafc45343a197973fc1d77f9740adf65769` | 6453 | `fnd/hc3` `drafts/hc3/reviewed-pairs.json` | the apply script's citation guard (`citations-reread.md`, last section) |
| `hc3/sc.md` | `b94932ed0253247254ed8e1d45ffd7421665221ec0002780c3a08351298e9fba` | 22259 | `fnd/hc3` `drafts/sc.md` | the layer 3 closer's session choices, numbered in `v2/ecad/tools/pcb_requirements.yaml` |
| `hc5/c5-response.md` | `f9bfc527e93eb732d078b00e4565baf1d33457aa0c2a333139d9f540bd5fc0f3` | 12430 | `fnd/hc5` `drafts/c5-response.md` | `v2/docs/HW-FW-CONTRACT.md` (section 10); the targeted fixer c5's answer to each finding |
| `hc5/drafts-README.md` | `5a192c631d126e94e85460211e624d730895f948fa92bb2151fbe432f40fa898` | 13726 | `fnd/hc5` `drafts/hc5/README.md` | the layer 5 closer's integration kit and hand-offs |
| `hc5/zer/run-100kHz.txt` | `78d55deca484b504a0382af29f1af1891599b2354594672c665157a4f153aeed` | 1057 | `fnd/hc5` `drafts/hc5/zer/run-100kHz.txt` | the same budget at 100 kHz, for comparison |
| `hc5/zer/run-90kHz.txt` | `2c907bc91dc19c0d42e78dfedc9819bcb292931990e78cc275616e488cd7283c` | 1056 | `fnd/hc5` `drafts/hc5/zer/run-90kHz.txt` | `v2/docs/feasibility/ZEROIZE.md` (section 3.4)<br>`v2/docs/HW-FW-CONTRACT.md` (section 6.4) |
| `hc5/zer/zer_budget.py` | `462660aeb39442cc2f7669fb4d3c6334601a5864643ebcd49260d49898ea6b6f` | 20300 | `fnd/hc5` `drafts/hc5/zer/zer_budget.py` (records/rv-zer's budget with F_I2C = 90 kHz; its header's 'not declared anywhere' sentence predates FW-K01 and is kept as filed) | `v2/docs/feasibility/ZEROIZE.md` (section 3.4, the budget at 90 kHz)<br>`v2/docs/HW-FW-CONTRACT.md` (section 6.4) |
| `hc7/APPLY.txt` | `0bf22ddec89e533a94a8a71a92c891b558df1cb306f706189882569b7b1f6511` | 12553 | `fnd/hc7` `drafts/hc7/APPLY.txt` | how the layer 7 closer's drafts landed (this integration) |
| `hc7/c7-response.md` | `b30096c739e99b39902594d3b54b44095d596831b985367a22bcf7ddbb39a7ff` | 17292 | `fnd/hc7` `drafts/c7-response.md` | the targeted fixer c7's answer to each finding, with the QMX tray's engineering question |
| `hc7/check_pcb_c-retake-pass2.txt` | `36e61cdf42cc6dedfb5b09d9a5cf596091ec96400c6dfaa01ad4eab0d03d8785` | 2392 | `fnd/hc7` `drafts/hc7/records/check_pcb_c-retake-pass2.txt` | `v2/docs/CASE-FIT-UNCERTAINTIES.md` (section 4) |
| `hc7/check_pcb_c-retake.txt` | `762783a7fc0432d0d65660bdc297d7ea3ea5e1858706bfc82609240838bf143d` | 2315 | `fnd/hc7` `drafts/hc7/records/check_pcb_c-retake.txt` | `v2/docs/CASE-FIT-UNCERTAINTIES.md` (section 4) |
| `hc7/check_pcb_c.e3aedb25.verdict.json` | `b886198a07ce06813a030607dcbeb19ee5ac1223f8ea2c8fac5147c9d9ad8bf4` | 1530 | `fnd/hc7` `drafts/hc7/records/check_pcb_c.e3aedb25.verdict.json` | `v2/docs/CASE-FIT-UNCERTAINTIES.md` (section 4) |
| `hc7/check_pcb_c.hc7.txt` | `3a60ff289e06c41814eddf686ae73fa685766a8990515f7c059395dddc1b350c` | 32000 | `fnd/hc7` `drafts/hc7/records/check_pcb_c.hc7.txt` | `v2/docs/CASE-FIT-UNCERTAINTIES.md` (section 4) |
| `hc7/check_pcb_c.hc7.verdict.json` | `43417b3cf91e355d764e07c82f04cb8aa0543982be4a6afe72125fb4dba19707` | 1530 | `fnd/hc7` `drafts/hc7/records/check_pcb_c.hc7.verdict.json` | `v2/docs/CASE-FIT-UNCERTAINTIES.md` (section 4) |
| `hc7/check_pcb_c.hc7p2-nozstack.txt` | `9fa06e1d287d382d402806284a65656238d2b470eca685dc4652e9028aa6c5a3` | 543 | `fnd/hc7` `drafts/hc7/records/check_pcb_c.hc7p2-nozstack.txt` | `v2/docs/CASE-FIT-UNCERTAINTIES.md` (section 4) |
| `hc7/check_pcb_c.hc7p2-nozstack.verdict.json` | `2bfe60cd7f3b331e76ad44e6104648cad40aab8fe76efdb31b887a1c67ccedaf` | 1920 | `fnd/hc7` `drafts/hc7/records/check_pcb_c.hc7p2-nozstack.verdict.json` | `v2/docs/CASE-FIT-UNCERTAINTIES.md` (section 4) |
| `hc7/check_pcb_c.hc7p2.txt` | `eda1a95e92c94c00a6dd8140388270e25f2a7ae8e3c866de8b170f260367b38f` | 32250 | `fnd/hc7` `drafts/hc7/records/check_pcb_c.hc7p2.txt` | `v2/docs/CASE-FIT-UNCERTAINTIES.md` (section 4) |
| `hc7/check_pcb_c.hc7p2.verdict.json` | `e7c67eec314c57719cdc7cd3c6b6829e5738afe34b7eeeba45469bd14c03c7d2` | 1896 | `fnd/hc7` `drafts/hc7/records/check_pcb_c.hc7p2.verdict.json` | `v2/docs/CASE-FIT-UNCERTAINTIES.md` (section 4) |
| `r4a/r4-decisions.md` | `2e5a0c20fc9d4f25d70d3defda2aaee056ed6b340584447fddc711898377bee2` | 101439 | `fnd/r4a` `drafts/r4-decisions.md` | `v2/docs/feasibility/EMCON.md`<br>`v2/docs/feasibility/POWER-THERMAL.md` |
| `r4a/r4-open-items.md` | `0c58f8a3574801b15b39ae06e377710e4c41646fe71d2dd81c8257733d259c91` | 27963 | `fnd/r4a` `drafts/r4-open-items.md` | `v2/docs/feasibility/POWER-THERMAL.md` |
| `r4b/box/r6-run6/README.txt` | `3977a8c3646ec82921c9bb2be1103f2c3ad55b192178ed2ac849e1d999ecbfae` | 1877 | `fnd/r4b` `drafts/box/r6-run6/README.txt` | `v2/docs/feasibility/FAILOVER-FABRIC.md` |
| `r4b/box/r6-run6/SHA256SUMS` | `eab4a7fbb05cfec2d88d4dbb52e67d85b8800698e2aeadc573580df558c08e0e` | 14282 | `fnd/r4b` `drafts/box/r6-run6/SHA256SUMS` | `v2/docs/feasibility/FAILOVER-FABRIC.md` |
| `r4b/box/r6-run6/check_pcb_b/emul-r6-gate-on-round6.txt` | `3ed0cc3868ff2b40e768a4bbfb2453bf1e28e2b4661db74e6b5ddd458861a7ab` | 19470 | `fnd/r4b` `drafts/box/r6-run6/check_pcb_b/emul-r6-gate-on-round6.txt` | `v2/docs/feasibility/FAILOVER-FABRIC.md` |
| `r8b/r8-decisions.md` | `edf91d080578c6a79678dd97105470adf3045f39ef37ee89ec2011e4a6177a5a` | `e7b6ce63b57f917145a819384fb71222cfd553002f481eb99f490d35fcdc303b` | two rows' PCIe switch name (PI7C9X2G304 to PI7C9X2G404SL, the first independent check), a filing note under the header and section 6, the integration |
| `r4b/box/r6-run6/parity_netlist_t6_tint.json` | `4b7e4a072b4d6a964a8d60e36a64cb2566d8422f9f27d114d354305fc5fa9091` | 716 | `fnd/r4b` `drafts/box/r6-run6/parity_netlist_t6_tint.json` | `v2/docs/feasibility/FAILOVER-FABRIC.md` |
| `r4b/box/r6-run6/run.log` | `a1b51495cf05f4961997bf4537eb87e0d50ce6881125a6cfcb67ebd22702a1a2` | 17735 | `fnd/r4b` `drafts/box/r6-run6/run.log` | `v2/docs/feasibility/FAILOVER-FABRIC.md` |
| `r4b/box/r6-run6/tint/set.sha256` | `ad88fa59804dcf32afcf212a48669425070064447b0babaed845d94f6684d7de` | 1090 | `fnd/r4b` `drafts/box/r6-run6/tint/set.sha256` | `v2/docs/feasibility/FAILOVER-FABRIC.md` |
| `r4b/box/r6b_box6.sh` | `002275ffe884ab774b1f40d1a17ceec352d9f447f762c11f3565703aecf847a6` | 15476 | `fnd/r4b` `drafts/box/r6b_box6.sh` | `v2/docs/feasibility/FAILOVER-FABRIC.md` |
| `r4b/box/r6b_post6.sh` | `dcaf39a37f83f0b81f2306af04829d1c10107c53e5f0b450972e61087c5819f6` | 2084 | `fnd/r4b` `drafts/box/r6b_post6.sh` | `v2/docs/feasibility/FAILOVER-FABRIC.md` |
| `r4b/pin_parity.py` | `a36a9ffe82fbffd103795f241a5f5116bf595b413062d1edf48c20f8723a6f66` | 2157 | `fnd/r4b` `drafts/pin_parity.py` | `v2/docs/ARCHITECTURE.md`<br>`v2/docs/feasibility/FAILOVER-FABRIC.md`<br>`v2/ecad/tools/gen_sch_b.py` |
| `r4b/r4-decisions.md` | `27023b76fce3d48dd198c64a43952f4e5632730bb9087cf7b793dcaf3166e671` | 103862 | `fnd/r4b` `drafts/r4-decisions.md` | `v2/docs/feasibility/EMCON.md`<br>`v2/docs/feasibility/FAILOVER-FABRIC.md`<br>`v2/ecad/tools/gen_sch_b.py` |
| `r4b/r4-interfaces.md` | `dafa398fa1c82e471c5292acc3e0e566727ea0a355856d4a56b40bb745349922` | 11702 | `fnd/r4b` `drafts/r4-interfaces.md` | `v2/docs/feasibility/FAILOVER-FABRIC.md`<br>`v2/ecad/tools/gen_sch_b.py` |
| `r4e/footprints/gen_footprint_sgp41.py` | `18555d1d239862def79025888cee91424869a440674d4148e37de4fb59e22a67` | 5516 | `fnd/r4e` `drafts/footprints/gen_footprint_sgp41.py` | `v2/release/review-packets/E-E17-1f614233` (`native/gen_sch_e.py`, `changes/gen_sch_e.diff`)<br>`v2/ecad/tools/gen_sch_e.py` |
| `r4e/jlc/jlc-SMCJ40CA.json` | `03d24c92aaf89b4c576244fd18fde13a7134b19261b8de9fe30c3cc24eea396f` | 64805 | `fnd/r4e` `drafts/jlc/jlc-SMCJ40CA.json` | `v2/release/review-packets/E-E17-1f614233` (`native/gen_sch_e.py`, `changes/gen_sch_e.diff`)<br>`v2/ecad/tools/gen_sch_e.py` |
| `r4e/jlc/jlc-SRF1260.json` | `312a2b79bf8b6083789373d8356965b70fc6f4c36f726a1884d7bfc2c5b93919` | 50446 | `fnd/r4e` `drafts/jlc/jlc-SRF1260.json` | `v2/release/review-packets/E-E17-1f614233` (`native/gen_sch_e.py`, `changes/gen_sch_e.diff`)<br>`v2/ecad/tools/gen_sch_e.py` |
| `r4e/jlc/jlc-SRF1260_1R0Y.json` | `abf447d72049bd2e716141a329383095f9189eb5873359b5c2b6ac6f0e960096` | 4046 | `fnd/r4e` `drafts/jlc/jlc-SRF1260_1R0Y.json` | `v2/release/review-packets/E-E17-1f614233` (`native/gen_sch_e.py`, `changes/gen_sch_e.diff`)<br>`v2/ecad/tools/gen_sch_e.py` |
| `r4e/jlc/jlc-SRF1260_1R5Y.json` | `813915919dbdb06595e93bd61128881e008b95d365ee7da8889e95b4b1561061` | 4056 | `fnd/r4e` `drafts/jlc/jlc-SRF1260_1R5Y.json` | `v2/release/review-packets/E-E17-1f614233` (`native/gen_sch_e.py`, `changes/gen_sch_e.diff`)<br>`v2/ecad/tools/gen_sch_e.py` |
| `r4e/jlc/jlc-SRF1260_2R2Y.json` | `40d3db2d4cd918a333958d6b673b99c92a9aa8516c88df7864d1dbe352f46664` | 88 | `fnd/r4e` `drafts/jlc/jlc-SRF1260_2R2Y.json` | `v2/release/review-packets/E-E17-1f614233` (`native/gen_sch_e.py`, `changes/gen_sch_e.diff`)<br>`v2/ecad/tools/gen_sch_e.py` |
| `r4e/jlc/jlc-SRF1260_4R7Y.json` | `571681216f60a8429888d8633300343b614e9a9edf7041a8c9a825ac965da450` | 4057 | `fnd/r4e` `drafts/jlc/jlc-SRF1260_4R7Y.json` | `v2/release/review-packets/E-E17-1f614233` (`native/gen_sch_e.py`, `changes/gen_sch_e.diff`)<br>`v2/ecad/tools/gen_sch_e.py` |
| `r4e/jlc/jlc-SRF1260_R47Y.json` | `e42554d2b11ae1eca2c3956350e8336d9a22bb49bba813b90a0884976586c793` | 4050 | `fnd/r4e` `drafts/jlc/jlc-SRF1260_R47Y.json` | `v2/release/review-packets/E-E17-1f614233` (`native/gen_sch_e.py`, `changes/gen_sch_e.diff`)<br>`v2/ecad/tools/gen_sch_e.py` |
| `r4e/jlc/jlc-SRF1280.json` | `ca5dcc1a57c5195ad721a2d21056b54f7ce00038302361df7d56c6e4cf64d617` | 51488 | `fnd/r4e` `drafts/jlc/jlc-SRF1280.json` | `v2/release/review-packets/E-E17-1f614233` (`native/gen_sch_e.py`, `changes/gen_sch_e.diff`)<br>`v2/ecad/tools/gen_sch_e.py` |
| `r4e/lcsc/C158012.json` | `cde2f69a427c8dba96daff2170dfbce1fa19f0ccebe35a37a5d36a45f81bffe5` | 49788 | `fnd/r4e` `drafts/lcsc/C158012.json` | `v2/release/review-packets/E-E17-1f614233` (`native/gen_sch_e.py`, `changes/gen_sch_e.diff`)<br>`v2/ecad/tools/gen_sch_e.py` |
| `r4e/lcsc/C224047.json` | `ccb876725c2b9c137f5c49f3dcfc7f2a3de018d72ad1bed82cf0c7ce9cfb7351` | 5903 | `fnd/r4e` `drafts/lcsc/C224047.json` | `v2/release/review-packets/E-E17-1f614233` (`native/gen_sch_e.py`, `changes/gen_sch_e.diff`)<br>`v2/ecad/tools/gen_sch_e.py` |
| `r4e/lcsc/C224052.json` | `9acc3b7108f79cf4236161071172e6188da0df239a72b55e273daa183a7e65d7` | 5941 | `fnd/r4e` `drafts/lcsc/C224052.json` | `v2/release/review-packets/E-E17-1f614233` (`native/gen_sch_e.py`, `changes/gen_sch_e.diff`)<br>`v2/ecad/tools/gen_sch_e.py` |
| `r4e/lcsc/C22935.json` | `e7728cf5be7be716a55badd66dc259883b6f2da81ec92f3d6b6c4704ba676f0f` | 32715 | `fnd/r4e` `drafts/lcsc/C22935.json` | `v2/release/review-packets/E-E17-1f614233` (`native/gen_sch_e.py`, `changes/gen_sch_e.diff`)<br>`v2/ecad/tools/gen_sch_e.py` |
| `r4e/lcsc/C3659325.json` | `a86e135fd9e76049a75c577cf98b0b67134bf05ac5638e61ac1583ded0e2f901` | 47 | `fnd/r4e` `drafts/lcsc/C3659325.json` | `v2/release/review-packets/E-E17-1f614233` (`native/gen_sch_e.py`, `changes/gen_sch_e.diff`)<br>`v2/ecad/tools/gen_sch_e.py` |
| `r4e/lcsc/C374030.json` | `a9b666c5696b401c642388fe91382eb8712c56f01ed2ac69137210f949e2c29a` | 5675 | `fnd/r4e` `drafts/lcsc/C374030.json` | `v2/release/review-packets/E-E17-1f614233` (`native/gen_sch_e.py`, `changes/gen_sch_e.diff`)<br>`v2/ecad/tools/gen_sch_e.py` |
| `r4e/lcsc/C527679.json` | `a8801ce55f07efa4260cbca20fe99e5f34ffefc24384ce298c5bf2b17d38f382` | 12519 | `fnd/r4e` `drafts/lcsc/C527679.json` | `v2/release/review-packets/E-E17-1f614233` (`native/gen_sch_e.py`, `changes/gen_sch_e.diff`)<br>`v2/ecad/tools/gen_sch_e.py` |
| `r4e/lcsc/C594232.json` | `8e3fc7b9b96afa00f1962da7129a8ece1a4c0d8b989f31bce6636490013871e1` | 48514 | `fnd/r4e` `drafts/lcsc/C594232.json` | `v2/release/review-packets/E-E17-1f614233` (`native/gen_sch_e.py`, `changes/gen_sch_e.diff`)<br>`v2/ecad/tools/gen_sch_e.py` |
| `r4e/lcsc/C7320434.json` | `0373b93f0dcfff998c5cdca69fcdddace6d73b2ddb55665e46f3e4547521a7b0` | 31301 | `fnd/r4e` `drafts/lcsc/C7320434.json` | `v2/release/review-packets/E-E17-1f614233` (`native/gen_sch_e.py`, `changes/gen_sch_e.diff`)<br>`v2/ecad/tools/gen_sch_e.py` |
| `r4e/lcsc/C80273.json` | `e19c409d1d5cc11dfcffee7c5ca7e5657250e6789205a175b3aaa7a8ce1051f7` | 5683 | `fnd/r4e` `drafts/lcsc/C80273.json` | `v2/release/review-packets/E-E17-1f614233` (`native/gen_sch_e.py`, `changes/gen_sch_e.diff`)<br>`v2/ecad/tools/gen_sch_e.py` |
| `r4e/r4-decisions.md` | `e05a31a54cfe5b9ec1159a110dc3bd6f0f0bbb8ed87cdd753d0e81fdd012f450` | 62162 | `fnd/r4e` `drafts/r4-decisions.md` | `v2/release/review-packets/E-E17-1f614233` (`native/gen_sch_e.py`, `changes/gen_sch_e.diff`)<br>`v2/ecad/tools/gen_sch_e.py`<br>`v2/ecad/tools/gen_pcb_e.py` |
| `r4p/datasheets/SOURCES.txt` | `dc8f584ca53c085dcd3fa7634cbc8ae2f72b3b3b3cdd6496292acb318bcc812f` | 9785 | `fnd/r4p` `drafts/datasheets/SOURCES.txt` | `v2/release/review-packets/P-P4-1f614233` (`native/gen_sch_p.py`, `changes/gen_sch_p.diff`, `changes/changes.json`)<br>`v2/ecad/tools/gen_sch_p.py` |
| `r4p/datasheets/lcsc-urls.txt` | `20b48c3ee78175d919793a67181aab69693569e0c566427182c7d6eecc26732a` | 742 | `fnd/r4p` `drafts/datasheets/lcsc-urls.txt` | `v2/release/review-packets/P-P4-1f614233` (`native/gen_sch_p.py`, `changes/gen_sch_p.diff`, `changes/changes.json`)<br>`v2/ecad/tools/gen_sch_p.py` |
| `r4p/r4-decisions.md` | `bab45c321c0c367561fdffc11d56c04a5a6c07497ce3d11fb28dd7868b4e49a0` | 43964 | `fnd/r4p` `drafts/r4-decisions.md` | `v2/docs/feasibility/POWER-THERMAL.md`<br>`v2/release/review-packets/P-P4-1f614233` (`native/gen_sch_p.py`, `changes/gen_sch_p.diff`, `changes/changes.json`)<br>`v2/ecad/tools/gen_sch_p.py`<br>`v2/ecad/tools/gen_pcb_p3.py` |
| `r4p/scripts/netdiff.py` | `a3b05ba1fc0d9b13f8034169a26dbb48d3d284e00be6a96ba27b495777b421be` | 3534 | `fnd/r4p` `drafts/scripts/netdiff.py` | `v2/docs/review-packets/battery/evidence/regeneration/netdiff.py` |
| `r4p/scripts/r5p2_box.sh` | `af7d59d6a8da41beb8cfa21b0e14b17652afb395863b623797d6eb026e90bdcd` | 10587 | `fnd/r4p` `drafts/scripts/r5p2_box.sh` | `v2/docs/review-packets/battery/evidence/regeneration/bat_box.sh` |
| `r4t/r4-decisions.md` | `833218028f012e008d20db38204d574e1b511661ae92be353f4f564578b6fcda` | 216568 | `fnd/r4t` `drafts/r4-decisions.md` | `v2/docs/feasibility/EMCON.md` |
| `r6d/r6-decisions.md` | `959ee8c6b9bf4e6622a81d858775b099e5e8637d6fc19d8dc263b13accac3ca1` | 32654 | `fnd/r6d` `drafts/r6-decisions.md` | `v2/docs/feasibility/EMCON.md` |
| `r8b/datasheets/SHA256SUMS` | `47ed7a46a52d4327eebc0ebbeca17e43165c656449240e2112dbc450ef65a045` | 427 | `fnd/r8b` `drafts/b/datasheets/SHA256SUMS` | the fetch record of the five maker documents filed in `v2/vendor/` (section below) |
| `r8b/datasheets/SOURCES.txt` | `6d8f2f194b036c5c2d7bac6d47334b6fd6d1ba66b6d56269ae6af8206913e2b7` | 2603 | `fnd/r8b` `drafts/b/datasheets/SOURCES.txt` | the fetch record of the five maker documents filed in `v2/vendor/` (section below) |
| `r8b/decoupling-classes-b.json` | `1b92ba7c91697d6f241a3bcd94fe6fd46ef4f0f4dc3bd7f72f3213b9a8180fd1` | 56766 | `fnd/r8b` `drafts/b/decoupling-classes-b.json` | `v2/docs/feasibility/DECOUPLING.md` (section 10) |
| `r8b/evidence/bbm-bounds.json` | `2602be7188b1cb1fa574ad1e1c85d41c7d7bdb3b0843f128c1777b2d81c315e7` | 1120 | `fnd/r8b` `drafts/b/evidence/bbm-bounds.json` | board B's round 8 commit (MESHSAT-1357); `r8b/r8-decisions.md` |
| `r8b/evidence/bbm-sim-main-hazard.txt` | `5c3aee27042797b01aa4fae4c737cbe45bb617d831c2cd2a5e8bbd8901f0b92a` | 2197 | `fnd/r8b` `drafts/b/evidence/bbm-sim-main-hazard.txt` | board B's round 8 commit (MESHSAT-1357); `r8b/r8-decisions.md` |
| `r8b/evidence/bbm-sim-main.txt` | `34a1505e7b066c2ac4197c43d1c117e642aaf54c05ca6be9f6c9239bc122c444` | 2198 | `fnd/r8b` `drafts/b/evidence/bbm-sim-main.txt` | board B's round 8 commit (MESHSAT-1357); `r8b/r8-decisions.md` |
| `r8b/evidence/bbm-sim-pass1-hazard.txt` | `1d6c8f4d9a4df583d17b1d2d131aeefd697b3be4b57cf50a130472d6463644bb` | 2901 | `fnd/r8b` `drafts/b/evidence/bbm-sim-pass1-hazard.txt` | board B's round 8 commit (MESHSAT-1357); `r8b/r8-decisions.md` |
| `r8b/evidence/bbm-sim-pass1.txt` | `403f64cef0294ad91802c1599151976f6d5069d63ad3717ad9356a766a6a05c0` | 2899 | `fnd/r8b` `drafts/b/evidence/bbm-sim-pass1.txt` | board B's round 8 commit (MESHSAT-1357); `r8b/r8-decisions.md` |
| `r8b/evidence/bbm-sim-pass2-hazard.txt` | `4de4fc11f847fb66a18ab40bff8bdac1f1fd08e4ae204322f68ac7b2c452546b` | 894 | `fnd/r8b` `drafts/b/evidence/bbm-sim-pass2-hazard.txt` | board B's round 8 commit (MESHSAT-1357); `r8b/r8-decisions.md` |
| `r8b/evidence/bbm-sim-pass2.txt` | `fa796caed4b84e0531e33496326735cb0659da0349ed9d60375b1215895976cd` | 895 | `fnd/r8b` `drafts/b/evidence/bbm-sim-pass2.txt` | board B's round 8 commit (MESHSAT-1357); `r8b/r8-decisions.md` |
| `r8b/evidence/check_pcb_b-r8-mutations.txt` | `7f55d8a20d167f899b9f0deed6b5fc5bdd47ee5936bd33e11b31c6ff8cb08ccf` | 2057 | `fnd/r8b` `drafts/b/evidence/check_pcb_b-r8-mutations.txt` | board B's round 8 commit (MESHSAT-1357); `r8b/r8-decisions.md` |
| `r8b/evidence/emul-patched-gate-on-main-net.txt` | `236624fcfb100cd2a628ac7eec478d3f8075b1b774dc9bb614ca4366076f1e1a` | 28832 | `fnd/r8b` `drafts/b/evidence/emul-patched-gate-on-main-net.txt` | board B's round 8 commit (MESHSAT-1357); `r8b/r8-decisions.md` |
| `r8b/evidence/emul-patched-gate-on-pass1-net.txt` | `d0fdc72a8e1e899823c13ed8c4a15e41ad45c8123f0564a37c706bc8f4c484b6` | 29479 | `fnd/r8b` `drafts/b/evidence/emul-patched-gate-on-pass1-net.txt` | board B's round 8 commit (MESHSAT-1357); `r8b/r8-decisions.md` |
| `r8b/evidence/emul-patched-gate-on-r8-net.txt` | `de21621f72dc039ace54af678702b8bb1073977f2b039cfafb77a04b9070187f` | 30014 | `fnd/r8b` `drafts/b/evidence/emul-patched-gate-on-r8-net.txt` | board B's round 8 commit (MESHSAT-1357); `r8b/r8-decisions.md` |
| `r8b/evidence/integrated-candidate-apply.log` | `fb945ea0af622ea52020515f44d0d0497bccda43fc70e56d6f99dce7ca25963f` | 3276 | `fnd/r8b` `drafts/b/evidence/integrated-candidate-apply.log` | board B's round 8 commit (MESHSAT-1357); `r8b/r8-decisions.md` |
| `r8b/evidence/integrated-check_contracts.verdict.json` | `056dd780d5561f0aeda750b4ccd064c2d42af58070c49b03731f0368b740bc3f` | 2299 | `fnd/r8b` `drafts/b/evidence/integrated-check_contracts.verdict.json` | board B's round 8 commit (MESHSAT-1357); `r8b/r8-decisions.md` |
| `r8b/evidence/integrated-energy_chain.verdict.json` | `cc8da6206776ed0ddc5933b79dc5af9df9f8962ed805c2d23d9fd17b7f0a2d7f` | 2032 | `fnd/r8b` `drafts/b/evidence/integrated-energy_chain.verdict.json` | board B's round 8 commit (MESHSAT-1357); `r8b/r8-decisions.md` |
| `r8b/evidence/integrated-energy_chain_b.verdict.json` | `e4961bf44923c99595a92129a2f2eb76a0c041921d640b9f1f9d40d3d6481b71` | 1165 | `fnd/r8b` `drafts/b/evidence/integrated-energy_chain_b.verdict.json` | board B's round 8 commit (MESHSAT-1357); `r8b/r8-decisions.md` |
| `r8b/evidence/integrated-inhibit_chain_a.verdict.json` | `264d7cab8460a68d5254e09cdbfa7ab844f517a85856e5c5ea389cdbd043a974` | 2293 | `fnd/r8b` `drafts/b/evidence/integrated-inhibit_chain_a.verdict.json` | board B's round 8 commit (MESHSAT-1357); `r8b/r8-decisions.md` |
| `r8b/evidence/integrated-inhibit_chain_b.verdict.json` | `9fd6f6b239cd429eeb68b2f49dadfce60ae211faa4450b7a2799a578afd8917a` | 2038 | `fnd/r8b` `drafts/b/evidence/integrated-inhibit_chain_b.verdict.json` | board B's round 8 commit (MESHSAT-1357); `r8b/r8-decisions.md` |
| `r8b/evidence/integrated-inhibit_chain_c.verdict.json` | `e37fce51280965eb95a34deb4e371b0b354ccf1ccd359d0c086b2a6a69c200ce` | 2038 | `fnd/r8b` `drafts/b/evidence/integrated-inhibit_chain_c.verdict.json` | board B's round 8 commit (MESHSAT-1357); `r8b/r8-decisions.md` |
| `r8b/evidence/integrated-inhibit_chain_d.verdict.json` | `45a2c250cdb632a3c240f9a21d9b801a4d427e844b6963cb7b4d57b9670c0482` | 2038 | `fnd/r8b` `drafts/b/evidence/integrated-inhibit_chain_d.verdict.json` | board B's round 8 commit (MESHSAT-1357); `r8b/r8-decisions.md` |
| `r8b/evidence/netdiff-committed-vs-r8b.json` | `3038a9dd158682f999bf0fbe88b0763ca24e7cfa6d989448d262ea217916ba21` | 46510 | `fnd/r8b` `drafts/b/evidence/netdiff-committed-vs-r8b.json` | board B's round 8 commit (MESHSAT-1357); `r8b/r8-decisions.md` |
| `r8b/evidence/netdiff-expected-r8b.txt` | `be15851fee7366c6331cb89064c205952897f4b6ca8b51fb8eeeed1fc2c12bb9` | 93 | `fnd/r8b` `drafts/b/evidence/netdiff-expected-r8b.txt` | board B's round 8 commit (MESHSAT-1357); `r8b/r8-decisions.md` |
| `r8b/evidence/netdiff-pass1-vs-pass2.json` | `8405dc15ec1c9dfa946d4774e7608b882f6e27724885a66339f36115d568dad0` | 14444 | `fnd/r8b` `drafts/b/evidence/netdiff-pass1-vs-pass2.json` | board B's round 8 commit (MESHSAT-1357); `r8b/r8-decisions.md` |
| `r8b/evidence/parity_intent_committed_clean.json` | `607f2e1b7adb75dc66267217a7334114126f37ea6ca8cab0548736b90c1ba3d4` | 76 | `fnd/r8b` `drafts/b/evidence/parity_intent_committed_clean.json` | board B's round 8 commit (MESHSAT-1357); `r8b/r8-decisions.md` |
| `r8b/evidence/parity_netlist_committed_clean.json` | `9003958c6e90294adf9eabf8664040faca5a284695679cf7769c0f53a52051cc` | 722 | `fnd/r8b` `drafts/b/evidence/parity_netlist_committed_clean.json` | board B's round 8 commit (MESHSAT-1357); `r8b/r8-decisions.md` |
| `r8b/evidence/parity_schematic_committed_clean.json` | `537b6e103625920221674cff9186aa8343fec27f8b6fda789cd377611551c626` | 351 | `fnd/r8b` `drafts/b/evidence/parity_schematic_committed_clean.json` | board B's round 8 commit (MESHSAT-1357); `r8b/r8-decisions.md` |
| `r8b/evidence/suite-commit-set-line.txt` | `c76325a8a1431cd211c0ca24de8db74c7ad5b05131215a0c4b4647ea9f28598c` | 571 | `fnd/r8b` `drafts/b/evidence/suite-commit-set-line.txt` | board B's round 8 commit (MESHSAT-1357); `r8b/r8-decisions.md` |
| `r8b/evidence/suite-commit-set-run.log` | `ac8f29fc51eb35dfd43a19f7f6f78a661759bd101044221d40fbf10bd6e20b2f` | 1072 | `fnd/r8b` `drafts/b/evidence/suite-commit-set-run.log` | board B's round 8 commit (MESHSAT-1357); `r8b/r8-decisions.md` |
| `r8b/evidence/suite-commit-set-status-delta.txt` | `d6225da747474bffe74f66a6e1f2db57d93f6230268711851d5ca0fd6589af26` | 274 | `fnd/r8b` `drafts/b/evidence/suite-commit-set-status-delta.txt` | board B's round 8 commit (MESHSAT-1357); `r8b/r8-decisions.md` |
| `r8b/evidence/suite-integrated-line.txt` | `010078b4287a054ae9b3da66bd68c8bc5f0f518ef586f8984e71d33f2f8109b8` | 40 | `fnd/r8b` `drafts/b/evidence/suite-integrated-line.txt` | board B's round 8 commit (MESHSAT-1357); `r8b/r8-decisions.md` |
| `r8b/evidence/suite-integrated-status-delta.txt` | `e3b0c44298fc1c149afbf4c8996fb92427ae41e4649b934ca495991b7852b855` | 0 | `fnd/r8b` `drafts/b/evidence/suite-integrated-status-delta.txt` | board B's round 8 commit (MESHSAT-1357); `r8b/r8-decisions.md` |
| `r8b/evidence/t8-gates-run.log` | `8eb14cc2d2decc356530c67bb0059311e8ed1c42d1cd09ce8954b89b726dffcd` | 6332 | `fnd/r8b` `drafts/b/evidence/t8-gates-run.log` | board B's round 8 commit (MESHSAT-1357); `r8b/r8-decisions.md` |
| `r8b/evidence/t8s-sidecars-run.log` | `a4434864ceaf4e3b61994cc6ce71457850c4c85ea46bd6c6498850779891090f` | 3523 | `fnd/r8b` `drafts/b/evidence/t8s-sidecars-run.log` | board B's round 8 commit (MESHSAT-1357); `r8b/r8-decisions.md` |
| `r8b/expected_r8b.json` | `4ee4d56d6f92ad77f3edd1c2bce59d87552b3dee3f2b6c33a66f412cf2f9ca1f` | 17216 | `fnd/r8b` `drafts/b/expected_r8b.json` | board B's round 8 commit (MESHSAT-1357); `r8b/r8-decisions.md` |
| `r8b/integration/gates.txt` | `eacc7abe8f9aee5587ec7d4763d6f93698ab457f746b02415a4ac68a9810e058` | 7434 | the integration (branch `fnd/r8int3`), its scratch and the build box's `/root/r8int3/out` | board B's round 8 commit (MESHSAT-1357); `r8b/r8-decisions.md` |
| `r8b/integration/indep_author_vs_tree.txt` | `bbc7ab758c266264a2e144025276246484aca420464a649ec83dc4c71a60cdcf` | 170 | the integration (branch `fnd/r8int3`), its scratch and the build box's `/root/r8int3/out` | board B's round 8 commit (MESHSAT-1357); `r8b/r8-decisions.md` |
| `r8b/integration/indep_cmp.py` | `5190f103398fca28723f3cab50fbc72ba591c5fb3a6099ea9f0f85bf35302789` | 5182 | the integration (branch `fnd/r8int3`), its scratch and the build box's `/root/r8int3/out` | board B's round 8 commit (MESHSAT-1357); `r8b/r8-decisions.md` |
| `r8b/integration/indep_committed_vs_tree.txt` | `c133c1a19dd3f0c426887878f0ad162256e5c14a36ff7b46bd1ddfa8b04ab913` | 82 | the integration (branch `fnd/r8int3`), its scratch and the build box's `/root/r8int3/out` | board B's round 8 commit (MESHSAT-1357); `r8b/r8-decisions.md` |
| `r8b/integration/indep_dropped.txt` | `756f5ffbd94be8dfa51308016b74d510578f49c20fa0a2eb05e57c4127fd6572` | 1816 | the integration (branch `fnd/r8int3`), its scratch and the build box's `/root/r8int3/out` | board B's round 8 commit (MESHSAT-1357); `r8b/r8-decisions.md` |
| `r8b/integration/indep_mainregen_vs_tree.txt` | `c133c1a19dd3f0c426887878f0ad162256e5c14a36ff7b46bd1ddfa8b04ab913` | 82 | the integration (branch `fnd/r8int3`), its scratch and the build box's `/root/r8int3/out` | board B's round 8 commit (MESHSAT-1357); `r8b/r8-decisions.md` |
| `r8b/integration/r8int3_box.sh` | `7c0e5a07e99841879e641e71cddbe0cfc53c551528e161f9251b1653d9e629ee` | 16978 | the integration (branch `fnd/r8int3`), its scratch and the build box's `/root/r8int3/out` | board B's round 8 commit (MESHSAT-1357); `r8b/r8-decisions.md` |
| `r8b/integration/regen.log` | `aeb07c9f14476eb46e6f188ad80a2c174920d5f7c9287d0ac833dd5535ef9ae2` | 1109 | the integration (branch `fnd/r8int3`), its scratch and the build box's `/root/r8int3/out` | board B's round 8 commit (MESHSAT-1357); `r8b/r8-decisions.md` |
| `r8b/integration/set.log` | `ad258a530940b10a3b41bac437177218cdac783af634751241c0735395a9130d` | 13621 | the integration (branch `fnd/r8int3`), its scratch and the build box's `/root/r8int3/out` | board B's round 8 commit (MESHSAT-1357); `r8b/r8-decisions.md` |
| `r8b/mk_m2b_te2199119.py` | `3575429073cc1f281df064fa388ccdc052bf78b3a74a7e54a9ce616501a0c621` | 2376 | `fnd/r8b` `drafts/b/mk_m2b_te2199119.py` | `v2/ecad/tools/gen_footprints_b16.py` |
| `r8b/r8-decisions.md` | `e7b6ce63b57f917145a819384fb71222cfd553002f481eb99f490d35fcdc303b` | 37062 | `fnd/r8b` `drafts/r8-decisions.md` | `v2/ecad/tools/gen_sch_b.py`<br>`v2/docs/feasibility/EMCON.md`<br>`v2/docs/feasibility/FAILOVER-FABRIC.md` |
| `r8b/tools/bbm_sim_r8b.py` | `e82e97d4ae67f71eddcba7a40b2ab1a8fcdc5ba65d0abdbd26cd155c6d352afd` | 27525 | `fnd/r8b` `drafts/b/tools/bbm_sim_r8b.py` | `v2/docs/feasibility/FAILOVER-FABRIC.md` (section 9a) |
| `r8b/tools/check_pcb_b_emul.py` | `d0c969110721d8dadd7e4a818bf6e44ebc1c6b6790bbad065879e301930ef53b` | 3091 | `fnd/r8b` `drafts/b/tools/check_pcb_b_emul.py` | board B's round 8 commit (MESHSAT-1357); `r8b/r8-decisions.md` |
| `r8b/tools/check_pcb_b_r8_mutations.py` | `fd9c49d135fe958d3b73a6f2f0dc13e6ddaddcfde2a465107d04f51b1aac9a63` | 4730 | `fnd/r8b` `drafts/b/tools/check_pcb_b_r8_mutations.py` | board B's round 8 commit (MESHSAT-1357); `r8b/r8-decisions.md` |
| `r8b/tools/expected_r8b.py` | `f4977714d17799a16fc03e6c3972ce6151bf967fd0208a3f607067eb4d13f1bd` | 7208 | `fnd/r8b` `drafts/b/tools/expected_r8b.py` | board B's round 8 commit (MESHSAT-1357); `r8b/r8-decisions.md` |
| `r8b/tools/netdiff.py` | `46b64b144c1874748835230e6a03112eec324816ee348ebec7434858e31fd96e` | 3370 | `fnd/r8b` `drafts/b/tools/netdiff.py` | board B's round 8 commit (MESHSAT-1357); `r8b/r8-decisions.md` |
| `r8b/tools/netdiff_r8b.py` | `fa5ce1d6ef8107c0f2e166e8d5bf7820ddf12d4cc01ce7cdd7edc41e3dd1087d` | 6119 | `fnd/r8b` `drafts/b/tools/netdiff_r8b.py` | board B's round 8 commit (MESHSAT-1357); `r8b/r8-decisions.md` |
| `r8b/tools/r8b2_box.sh` | `df9826ad3da0e3bd3d7f8ea2102872f81989579296f08ed025c003fdfe9aadad` | 12701 | `fnd/r8b` `drafts/b/tools/r8b2_box.sh` | board B's round 8 commit (MESHSAT-1357); `r8b/r8-decisions.md` |
| `r8b/tools/rebind_r8b.py` | `7204e6d874065bc84253bb76f2b172ba2952d438bfe6cbe40b609d055f6ac644` | 8426 | `fnd/r8b` `drafts/b/tools/rebind_r8b.py` | board B's round 8 commit (MESHSAT-1357); `r8b/r8-decisions.md` |
| `r8d/r8d-gates.txt` | `b32af9bc5bf5ac1c04f04ee18a0f1656a1106cde273f8c98a9dd38c2b1c73c1d` | 3731 | `fnd/r8d` `drafts/d/records/r8d-gates.txt` | board D's round 8 commit (MESHSAT-1357) |
| `r8d/r8d-par.txt` | `064ae27b66f8bcff68ea377c14b0dbe415797814d70f8a9492bbc182fc940804` | 29949 | `fnd/r8d` `drafts/d/records/r8d-par.txt` | board D's round 8 commit (MESHSAT-1357) |
| `r8d/r8d-parity-and-suite.txt` | `c763a2930bcc1e920a77093c6900e559a5e5323925083f9d33d4c6f4b3e80654` | 5185 | `fnd/r8d` `drafts/d/records/r8d-parity-and-suite.txt` | board D's round 8 commit (MESHSAT-1357) |
| `r8d/r8d_par.py` | `72b766f7221008599ce1272d0b6bd118081194d9dc2b65aadf718ca87ce135f4` | 15435 | `fnd/r8d` `drafts/d/records/r8d_par.py` | board D's round 8 commit (MESHSAT-1357) |
| `r8d/r8d_regen.sh` | `297651d22f4e3797360fb6517080c6a2e52865d81da9052aec7f0507dc155db1` | 8865 | `fnd/r8d` `drafts/d/records/r8d_regen.sh` | board D's round 8 commit (MESHSAT-1357) |
| `r8d/r8d_set.sh` | `fa34ed5489c48ab438c3d9e98c465e8cdec35c5c4ce16a8ff092325496070a64` | 5804 | `fnd/r8d` `drafts/d/records/r8d_set.sh` | board D's round 8 commit (MESHSAT-1357) |
| `r8d/r8d_suite.sh` | `c6ce1bdea945d1e606500e3f10dad8aa192e6b4609ff46d73080b9311e8efdc8` | 4908 | `fnd/r8d` `drafts/d/records/r8d_suite.sh` | board D's round 8 commit (MESHSAT-1357) |
| `r8int4/c23-apply-registry.log` | `58ba20cf0bc76a485419303b4c4809b715f93f0cd98f868b0d712239f01b562c` | 26515 | `fnd/r8int4` (the integrator's scratch, filed at integration), the apply script's output | the registry change of this integration |
| `r8int4/changed_sections.py` | `8669cd02987474d41325f7bc72f1f0301c38fdf4a3f38d22e2ae8755b3f18ed7` | 856 | `fnd/r8int4` (the integrator's scratch, filed at the release check of layers 1 to 3) | the section lists of `post_release_registry.py`'s evidence entries |
| `r8int4/citations-reread-r8int4.md` | `d04ab7bdc144337fdf1034dad2bed98aa510c0949b941de207daec3650a13fce` | 4400 | `fnd/r8int4` (the integrator's scratch, filed at integration) | `v2/ecad/tools/pcb_requirements.yaml` (CFL-016, REQ-052, CFL-006 evidence) |
| `r8int4/citations-reread-release.md` | `699d7a062db56cdc93db2ae8c35f773e59b8df07328a319eec2d99ddcfe85cbe` | 4582 | `fnd/r8int4` (the integrator's scratch, filed at the release check of layers 1 to 3) | `v2/ecad/tools/pcb_requirements.yaml` (sources_read_at and the ten moved citations)<br>`v2/docs/handover/START-HERE.md` (section 9)<br>`v2/docs/handover/LAYER-STATUS.md` (layer 3) |
| `r8int4/edit_c23_contradictions.py` | `148842e6c512fb93d9c4862965b3224796961ff5ec4e4be9e1ad67d3404de782` | 5678 | `fnd/r8int4` (the integrator's scratch, filed at integration) | `v2/docs/CONOPS.md`<br>`v2/docs/OPERATING-ENVELOPE.md`<br>`v2/ecad/tools/pcb_envelope.yaml` |
| `r8int4/edit_c5_handover.py` | `5de611c6e872d989bc98662069e8464ff21e1e54a9dc6fb73a26e59fa8238ad3` | 2781 | `fnd/r8int4` (the integrator's scratch, filed at integration) | the layer 5 merge of this integration (verify c5's contradictions and review 2's wording items) |
| `r8int4/edit_c5_wording.py` | `aa8e273b44d0f6fbb36a19ada033108bc4621f14f67994545ca2e2ab315e9712` | 6212 | `fnd/r8int4` (the integrator's scratch, filed at integration) | the layer 5 merge of this integration (verify c5's contradictions and review 2's wording items) |
| `r8int4/edit_c7_handover.py` | `f0762617c9fa426646e3d8184e8d499d517bdbd9f4a07bab67e1c4bd5c271978` | 3416 | `fnd/r8int4` (the integrator's scratch, filed at integration) | `v2/docs/handover/ENGINEERING-QUESTIONS.md`<br>`v2/docs/handover/CONTINUATION-BRIEF.md`<br>`v2/docs/handover/LAYER-STATUS.md` (verify c7) |
| `r8int4/edit_c7_timing.py` | `b48f87c634138cc7c4101dd68d53874f9c47b1d23c4d516fc0edcfafbf390560` | 7800 | `fnd/r8int4` (the integrator's scratch, filed at integration) | `v2/docs/reviews/READY-TO-ACT.md`<br>`v2/docs/ARCHITECTURE.md`<br>`v2/docs/layout-constraints/README.md`<br>`v2/docs/OPERATING-ENVELOPE.md`<br>`v2/docs/V2-SPEC.md` (verify c7) |
| `r8int4/edit_cfl010_reconcile.py` | `fd575e8ac00bd3a9e078b0df1496959c3fdf0b4bc9ffe62211357a570693d459` | 2280 | `fnd/r8int4` (the integrator's scratch, filed at integration) | `v2/docs/V2-SPEC.md`<br>`v2/docs/PRODUCT-BRIEF.md` |
| `r8int4/edit_handover_set4.py` | `606d07ead5432e0ea513da27091df65c21efd711244ae92909074df66a210469` | 27316 | `fnd/r8int4` (the integrator's scratch, filed at integration) | `v2/docs/handover/LAYER-STATUS.md`, `ENGINEERING-QUESTIONS.md`, `START-HERE.md`, `CONTINUATION-BRIEF.md` and `candidates/README.md` (set 4) |
| `r8int4/edit_layer2_emcon_face.py` | `fba349a250a52a651bd65b306a47c66a4431d238891619530d1ff55e5cd298f0` | 7547 | `fnd/r8int4` (the integrator's scratch, filed at integration) | `v2/docs/CONOPS.md`<br>`v2/docs/PANEL.md` (fnd/hc1's held patch re-derived) |
| `r8int4/edit_release_fixes.py` | `d8e6c67e6ccdcf37c8110b64a509b8a5b8c853ee31a9333dbebe32dc046897b2` | 40798 | `fnd/r8int4` (the integrator's scratch, filed at the release check of layers 1 to 3) | `v2/docs/PRODUCT-BRIEF.md`<br>`README.md`<br>`v2/README.md`<br>`v2/BUILD.md`<br>`v2/docs/V2-SPEC.md`<br>`v2/docs/CONOPS.md`<br>`v2/docs/OPERATING-ENVELOPE.md`<br>`v2/docs/TEST-PLAN.md`<br>`v2/docs/PANEL.md`<br>`v2/docs/handover/CONTINUATION-BRIEF.md` (the release reviews' wording and citation fixes) |
| `r8int4/edit_release_handover.py` | `a6f8fe8059c23c042aa3a7a78f20c2220605930c91fda39c92aae9ed9a4fdcc6` | 15780 | `fnd/r8int4` (the integrator's scratch, filed at the release check of layers 1 to 3) | `v2/docs/handover/LAYER-STATUS.md`<br>`v2/docs/handover/START-HERE.md` (the release check) |
| `r8int4/file_records.py` | `2eb2b099e40427d8be8665b08f12d40288b2fc3e04c47126a277aa2ace240ad3` | 1883 | `fnd/r8int4` (the integrator's scratch, filed at integration) | this README's rows for `hc2/`, `hc3/` and `r8int4/` |
| `r8int4/hc5/ARCHITECTURE-section-12.r8int4.md` | `0f7f6d132ba220749fd725931138f7a9b38f538afd55d6082c055738e20959c4` | 12032 | `fnd/r8int4` (the integrator's scratch, filed at integration): fnd/hc5's section 12 three-way merged with board B's round 8 IF-BC-PANEL row | `v2/docs/ARCHITECTURE.md` (section 12) |
| `r8int4/hc5/apply_architecture.py` | `98271ff6d858c4fe824633e60590a80b04ef918b5effe73bd6890955d8dc0b13` | 4967 | `fnd/r8int4` (the integrator's scratch, filed at integration), from `fnd/hc5` `drafts/hc5/apply_architecture.py`, re-anchored for `38dcd764` | the layer 5 merge of this integration |
| `r8int4/hc5/apply_docs.py` | `1bb7ba1bf8a5fbc82e552475eaaf7627bb3a71f3adb5ad6c413c452d097b8f58` | 22680 | `fnd/r8int4` (the integrator's scratch, filed at integration), from `fnd/hc5` `drafts/hc5/apply_docs.py`, re-anchored for `38dcd764` | the layer 5 merge of this integration |
| `r8int4/hc5/apply_index.py` | `0f410c7282375d67dee109751a10a308a70951ec2bc914418ada89d1d9c0a65d` | 4457 | `fnd/r8int4` (the integrator's scratch, filed at integration), from `fnd/hc5` `drafts/hc5/apply_index.py` | the layer 5 merge of this integration |
| `r8int4/hc5/apply_interfaces.py` | `b1101e8734307b6de3f25f0d38dfa4d49b98ae1c3a66151704c08c320d054456` | 6653 | `fnd/r8int4` (the integrator's scratch, filed at integration), from `fnd/hc5` `drafts/hc5/apply_interfaces.py` | the layer 5 merge of this integration |
| `r8int4/hc5/apply_registry.py` | `9b9782280d7092fda704f12681ba8ab5ee99ec969081cf122d5b77a3b4863fd2` | 13222 | `fnd/r8int4` (the integrator's scratch, filed at integration), from `fnd/hc5` `drafts/hc5/apply_registry.py`, re-anchored for `38dcd764` | the layer 5 merge of this integration |
| `r8int4/hc5/pcb_interfaces-new-contracts.yaml` | `996fa8d5e94dc18d51ae3510879e4662a149e2623fc495186b33171603829cd6` | 45049 | `fnd/r8int4` (the integrator's scratch, filed at integration), from `fnd/hc5` `drafts/hc5/pcb_interfaces-new-contracts.yaml` | the layer 5 merge of this integration |
| `r8int4/hc7/apply_registry.log` | `60f5f7ba90fdc2e3e67e3d3343aac2cdb6fa7a077fef4569ec8bbc3be283661c` | 859 | `fnd/r8int4` (the integrator's scratch, filed at integration), the script's output | the layer 7 merge of this integration |
| `r8int4/hc7/apply_registry.py` | `6dce16575775f48898700c126293002fd7a4ddbee7bc18228a364f606b3caa49` | 27028 | `fnd/r8int4` (the integrator's scratch, filed at integration), from `fnd/hc7` `drafts/hc7/apply_registry.py`, run unchanged with --rebind | the layer 7 merge of this integration (REQ-047, CON-006, L-07, FEA-007, CON-006 and REQ-019 rebound) |
| `r8int4/post_c23_registry.py` | `fb45b9a3d81169ad9741ec130058d135be725778e7d1a4a0591868584fb43621` | 5177 | `fnd/r8int4` (the integrator's scratch, filed at integration) | `v2/ecad/tools/pcb_requirements.yaml` (CFL-016, REQ-024, FEA-004) |
| `r8int4/post_c23_registry2.py` | `63266ee51d8741cf5e8054b6f6b2486bc6c59577d57ca0ed7e4f72f42bac96a8` | 2724 | `fnd/r8int4` (the integrator's scratch, filed at integration) | `v2/ecad/tools/pcb_requirements.yaml` (REQ-052, CFL-006) |
| `r8int4/post_c5_registry.py` | `1495de2ec9fd2e2052fc7993e1c940ea65e6470442becf9ec838e7d9d4e9607d` | 2876 | `fnd/r8int4` (the integrator's scratch, filed at integration) | the layer 5 merge of this integration (verify c5's contradictions and review 2's wording items) |
| `r8int4/post_c5_registry2.py` | `3694e7bfbbf6b173b75aacd0812c2a2443dd609cc5bbec408454a84d111278df` | 2075 | `fnd/r8int4` (the integrator's scratch, filed at integration) | the layer 5 merge of this integration (verify c5's contradictions and review 2's wording items) |
| `r8int4/post_c7_registry.py` | `f893ea52c36e15e92f062404295dd6ee67011f27db291166aa2517e63a37c8a6` | 7769 | `fnd/r8int4` (the integrator's scratch, filed at integration) | `v2/ecad/tools/pcb_requirements.yaml` (REQ-019, S-63 and the rebinds of the layer 7 merge) |
| `r8int4/post_release_evidence.py` | `6f94c7155cc6dbb38e82dc964f7317672c4feeec40d3e25eb390e1184f6025f6` | 2672 | `fnd/r8int4` (the integrator's scratch, filed at the release check of layers 1 to 3) | `v2/ecad/tools/pcb_requirements.yaml` (CON-010 and REQ-044 rebound to the rendered CURRENT-EVIDENCE.md) |
| `r8int4/post_release_registry.py` | `3ddaab0e42cee12b3c5f6a29d35332ad5e846903d996b79a5ad42627cc734dcd` | 12846 | `fnd/r8int4` (the integrator's scratch, filed at the release check of layers 1 to 3) | `v2/ecad/tools/pcb_requirements.yaml` (the rebinds, S-01 and S-44, the needs pin), `pcb_envelope.yaml`, `pcb_rules_coverage.yaml` (ENV-001) |
| `r8int4/reanchor.log` | `29b51f294297da3e390409378be32c1b7353e0f58f8af0a354270b105867591e` | 1868 | `fnd/r8int4` (the integrator's scratch, filed at integration), the re-anchoring's output | `v2/ecad/tools/pcb_requirements.yaml` |
| `r8int4/reanchor_only.py` | `c358c1e3fdb05da316f409f18fdb48cf2c297e93f4a4274c96451ea2d32b06a7` | 1305 | `fnd/r8int4` (the integrator's scratch, filed at integration) | `v2/ecad/tools/pcb_requirements.yaml` (sources_read_at and the carried citations) |
| `r8int4/reanchor_preview.py` | `a845aa44c7d6b9a94a0d8d711b5a3cee807f074b9f7df7c51ae91de0ff473152` | 925 | `fnd/r8int4` (the integrator's scratch, filed at the release check of layers 1 to 3) | `r8int4/citations-reread-release.md` (the preview of the apply script's re-anchoring) |
| `r8int4/reanchor_release.py` | `49e3859d68d3c03d4a7e9b11b1f9e0341101cce9c2113e2c9598588949883d15` | 4665 | `fnd/r8int4` (the integrator's scratch, filed at the release check of layers 1 to 3) | `v2/ecad/tools/pcb_requirements.yaml` (sources_read_at and the ten moved citations; the check of every source-field citation) |
| `r8int4/rebind_current_evidence.py` | `3da37cdd14064434bc8a46a53e98e7a7ffe7f3ec7d8b2307f53922c2769d237c` | 1518 | `fnd/r8int4` (the integrator's scratch, filed at integration) | `v2/ecad/tools/pcb_requirements.yaml` (CON-010 and REQ-044 after each render) |
| `r8int5/edlib.py` | `2675e3518a62d4ce6bca3ed1759a408c12d2c1059e34f639642f312d47060b9e` | 2205 | the r8int5 integrator (`edlib.py`) | the docs(evidence) commit of `fnd/r8int5` |
| `r8int5/file_stream.py` | `7c378336c0770b47adcdd82373f0b5dfcbc9e717e5972f124a37ce1580696c66` | 1804 | the r8int5 integrator (`file_stream.py`) | the docs(evidence) commit of `fnd/r8int5` |
| `r8int5/final-regen/a/parity_bom.json` | `5145580aba2011e2b5f33bb043e39677356bff43fef0c69f62fa928d20950422` | 68 | the r8int5 integrator (`final-regen/a/parity_bom.json`) | the docs(evidence) commit of `fnd/r8int5` |
| `r8int5/final-regen/a/parity_erc.json` | `75c8d22743f41d58885766af21fd940066b6cbb6132b7cd939e3314ec5d8b5c6` | 359 | the r8int5 integrator (`final-regen/a/parity_erc.json`) | the docs(evidence) commit of `fnd/r8int5` |
| `r8int5/final-regen/a/parity_intent.json` | `607f2e1b7adb75dc66267217a7334114126f37ea6ca8cab0548736b90c1ba3d4` | 76 | the r8int5 integrator (`final-regen/a/parity_intent.json`) | the docs(evidence) commit of `fnd/r8int5` |
| `r8int5/final-regen/a/parity_netlist.json` | `1889661518410c4c450d5ab5cce71c079ccf2b312a7612be0fbf7084e572523c` | 710 | the r8int5 integrator (`final-regen/a/parity_netlist.json`) | the docs(evidence) commit of `fnd/r8int5` |
| `r8int5/final-regen/a/parity_schematic.json` | `785d0297dafc79b7c6f22f72f9b4f0106e23bd314dce674116c445fcafa4fe70` | 351 | the r8int5 integrator (`final-regen/a/parity_schematic.json`) | the docs(evidence) commit of `fnd/r8int5` |
| `r8int5/final-regen/a/regen-pcb-a-power.net.prov.json` | `4fc1d645a434fbc16cf55c9a88b1fb29521ba78f8ed7352cf1e50d70f6ab66a2` | 8641 | the r8int5 integrator (`final-regen/a/regen-pcb-a-power.net.prov.json`) | the docs(evidence) commit of `fnd/r8int5` |
| `r8int5/final-regen/a/regen.json` | `340e78cc5e11a37f97490b20670fe7634dae4b422f673f2133ca9bf7ddfd1e41` | 4575 | the r8int5 integrator (`final-regen/a/regen.json`) | the docs(evidence) commit of `fnd/r8int5` |
| `r8int5/final-regen/b/parity_bom.json` | `da4625a57a36e599c5d9cff640a216be0efc29eba0bde764cdfa3069a6c3dd0c` | 68 | the r8int5 integrator (`final-regen/b/parity_bom.json`) | the docs(evidence) commit of `fnd/r8int5` |
| `r8int5/final-regen/b/parity_erc.json` | `58fbc1bb13978469fa5d013f5d380cda77cac95f7866f35fc349937a028496de` | 485 | the r8int5 integrator (`final-regen/b/parity_erc.json`) | the docs(evidence) commit of `fnd/r8int5` |
| `r8int5/final-regen/b/parity_intent.json` | `607f2e1b7adb75dc66267217a7334114126f37ea6ca8cab0548736b90c1ba3d4` | 76 | the r8int5 integrator (`final-regen/b/parity_intent.json`) | the docs(evidence) commit of `fnd/r8int5` |
| `r8int5/final-regen/b/parity_netlist.json` | `b06f5bc44c71cd89f80682b407eff7737424fdecd4248f3a2597a7ae16657549` | 717 | the r8int5 integrator (`final-regen/b/parity_netlist.json`) | the docs(evidence) commit of `fnd/r8int5` |
| `r8int5/final-regen/b/parity_schematic.json` | `ae0669e008778caeef8abacf82b910c30b6718d65ac96ed67c81e066696088a0` | 351 | the r8int5 integrator (`final-regen/b/parity_schematic.json`) | the docs(evidence) commit of `fnd/r8int5` |
| `r8int5/final-regen/b/regen-pcb-b-compute.net.prov.json` | `7f81042288ce056c3225c2a28a24f2e085cf2779d23b83e118faf315458cbd84` | 8643 | the r8int5 integrator (`final-regen/b/regen-pcb-b-compute.net.prov.json`) | the docs(evidence) commit of `fnd/r8int5` |
| `r8int5/final-regen/b/regen.json` | `250ffbf35ecca9d74c62478d96b4b186af3bc28fe8ecd3ed75b8882f53d82064` | 5699 | the r8int5 integrator (`final-regen/b/regen.json`) | the docs(evidence) commit of `fnd/r8int5` |
| `r8int5/final-regen/d/parity_bom.json` | `38a45a536d61f86d91b1ac10e9c8e865434582cdf930f8240588b3f8457a9509` | 66 | the r8int5 integrator (`final-regen/d/parity_bom.json`) | the docs(evidence) commit of `fnd/r8int5` |
| `r8int5/final-regen/d/parity_erc.json` | `360922074f67148628c93519ed75a6c9f9690e98a268f08800c9511596d34cd6` | 353 | the r8int5 integrator (`final-regen/d/parity_erc.json`) | the docs(evidence) commit of `fnd/r8int5` |
| `r8int5/final-regen/d/parity_intent.json` | `607f2e1b7adb75dc66267217a7334114126f37ea6ca8cab0548736b90c1ba3d4` | 76 | the r8int5 integrator (`final-regen/d/parity_intent.json`) | the docs(evidence) commit of `fnd/r8int5` |
| `r8int5/final-regen/d/parity_netlist.json` | `aed45b82852f0c562d4b5eb94b401de0c239a19865ea740eb7ad154900adae47` | 707 | the r8int5 integrator (`final-regen/d/parity_netlist.json`) | the docs(evidence) commit of `fnd/r8int5` |
| `r8int5/final-regen/d/parity_schematic.json` | `af98d012beb62c3341802f374720616c5c84b954b3ae08ed8dfdd133fac5dc32` | 349 | the r8int5 integrator (`final-regen/d/parity_schematic.json`) | the docs(evidence) commit of `fnd/r8int5` |
| `r8int5/final-regen/d/regen-pcb-d-aprs.net.prov.json` | `45c3b4b05a8b6305f650d5aeda2618a0e58c0c168cf4b51a676702ec97700e56` | 8640 | the r8int5 integrator (`final-regen/d/regen-pcb-d-aprs.net.prov.json`) | the docs(evidence) commit of `fnd/r8int5` |
| `r8int5/final-regen/d/regen.json` | `755cc0f8c0a65c1152310af58b6a44c2117545b1a61a247055b76858fefebcfe` | 5115 | the r8int5 integrator (`final-regen/d/regen.json`) | the docs(evidence) commit of `fnd/r8int5` |
| `r8int5/final-regen/e/parity_bom.json` | `09a7a85364829556cbc457c9d2050d8ae254742b3826ae1f6cd0e5f6843d8e9d` | 68 | the r8int5 integrator (`final-regen/e/parity_bom.json`) | the docs(evidence) commit of `fnd/r8int5` |
| `r8int5/final-regen/e/parity_erc.json` | `14039c7eaa246a5d372faaa999955a9803064d52dda9825485f196cb129abaa2` | 353 | the r8int5 integrator (`final-regen/e/parity_erc.json`) | the docs(evidence) commit of `fnd/r8int5` |
| `r8int5/final-regen/e/parity_intent.json` | `607f2e1b7adb75dc66267217a7334114126f37ea6ca8cab0548736b90c1ba3d4` | 76 | the r8int5 integrator (`final-regen/e/parity_intent.json`) | the docs(evidence) commit of `fnd/r8int5` |
| `r8int5/final-regen/e/parity_netlist.json` | `9b2c5ea9ce1bd5de72711cc8637cdb5eb7b36a0565aa418427c0c71298fd0a4e` | 711 | the r8int5 integrator (`final-regen/e/parity_netlist.json`) | the docs(evidence) commit of `fnd/r8int5` |
| `r8int5/final-regen/e/parity_schematic.json` | `ace929ea68219b80b5988bb0d9b42f9a99b6fdda1b7305c112faa594f6a07d7d` | 349 | the r8int5 integrator (`final-regen/e/parity_schematic.json`) | the docs(evidence) commit of `fnd/r8int5` |
| `r8int5/final-regen/e/regen-pcb-e1-dock.net.prov.json` | `640336eba8ab9e5b4dcf3b351b7b39e9b8e2eaa598f9d68cc272c88809db6130` | 8587 | the r8int5 integrator (`final-regen/e/regen-pcb-e1-dock.net.prov.json`) | the docs(evidence) commit of `fnd/r8int5` |
| `r8int5/final-regen/e/regen.json` | `0cd7489aa0506d604ef555390449805f5348ef7ea2514b38d106d93d590073e0` | 4791 | the r8int5 integrator (`final-regen/e/regen.json`) | the docs(evidence) commit of `fnd/r8int5` |
| `r8int5/logs/box-regen-a-dock.log` | `54261b664f9adf8570bdc2095f44cd09f8f29bf5d2e3d97286ed3817311ea001` | 227 | the r8int5 integrator (`logs/box-regen-a-dock.log`) | the docs(evidence) commit of `fnd/r8int5` **Not in the repository:** the rule `logs/` of `.gitignore` kept it out of every commit, and the file was lost with its worktree on 27 September 2026 |
| `r8int5/logs/box-regen-final.log` | `493d04292fae8122c32140e18886abd9b2079a7c7a44c19d90664f7102fa8cf8` | 938 | the r8int5 integrator (`logs/box-regen-final.log`) | the docs(evidence) commit of `fnd/r8int5` **Not in the repository:** the rule `logs/` of `.gitignore` kept it out of every commit, and the file was lost with its worktree on 27 September 2026 |
| `r8int5/logs/check_contracts-b7f96784.log` | `d5abb44f529170e57bb77d27401d6eaf73dbd53d75d5babe77fe18b8e58a8e81` | 22984 | the r8int5 integrator (`logs/check_contracts-b7f96784.log`) | the docs(evidence) commit of `fnd/r8int5` **Not in the repository:** the rule `logs/` of `.gitignore` kept it out of every commit, and the file was lost with its worktree on 27 September 2026 |
| `r8int5/logs/diagrams-build-b7f96784.log` | `373375e7546744817aea004bfc7250021ea8d20fbb8bf8ffb7757fbb3ab7cfb1` | 3830 | the r8int5 integrator (`logs/diagrams-build-b7f96784.log`) | the docs(evidence) commit of `fnd/r8int5` **Not in the repository:** the rule `logs/` of `.gitignore` kept it out of every commit, and the file was lost with its worktree on 27 September 2026 |
| `r8int5/logs/diagrams-readback-b7f96784.log` | `607a9811a96a655421304a212f62c9c1509631dcfb238f4a44357a9a88ec42e4` | 2682 | the r8int5 integrator (`logs/diagrams-readback-b7f96784.log`) | the docs(evidence) commit of `fnd/r8int5` **Not in the repository:** the rule `logs/` of `.gitignore` kept it out of every commit, and the file was lost with its worktree on 27 September 2026 |
| `r8int5/logs/rules_status-1.log` | `43f0b4877016cbed9a70ad668ef50ad7700cf4bf52331f93673b44dd574959b4` | 4068 | the r8int5 integrator (`logs/rules_status-1.log`) | the docs(evidence) commit of `fnd/r8int5` **Not in the repository:** the rule `logs/` of `.gitignore` kept it out of every commit, and the file was lost with its worktree on 27 September 2026 |
| `r8int5/logs/rules_status-2.log` | `5d59281cd5dcb43aa739204f8179640afe0812858fdff3455dadf961898b32a2` | 4068 | the r8int5 integrator (`logs/rules_status-2.log`) | the docs(evidence) commit of `fnd/r8int5` **Not in the repository:** the rule `logs/` of `.gitignore` kept it out of every commit, and the file was lost with its worktree on 27 September 2026 |
| `r8int5/logs/rules_status-3.log` | `5d59281cd5dcb43aa739204f8179640afe0812858fdff3455dadf961898b32a2` | 4068 | the r8int5 integrator (`logs/rules_status-3.log`) | the docs(evidence) commit of `fnd/r8int5` **Not in the repository:** the rule `logs/` of `.gitignore` kept it out of every commit, and the file was lost with its worktree on 27 September 2026 |
| `r8int5/logs/tests-w3b-targeted.log` | `6fccc2554c2c698012879a149eb3b69f12526f6c41176ed3c1151f6b5765eb6f` | 80876 | the r8int5 integrator (`logs/tests-w3b-targeted.log`) | the docs(evidence) commit of `fnd/r8int5` **Not in the repository:** the rule `logs/` of `.gitignore` kept it out of every commit, and the file was lost with its worktree on 27 September 2026 |
| `r8int5/logs/tests-w3de-targeted.log` | `0627374294ab7a04774149f626d42b6ea7b39a5efd85f9752005908cc7664bdd` | 110534 | the r8int5 integrator (`logs/tests-w3de-targeted.log`) | the docs(evidence) commit of `fnd/r8int5` **Not in the repository:** the rule `logs/` of `.gitignore` kept it out of every commit, and the file was lost with its worktree on 27 September 2026 |
| `r8int5/rebind_current_evidence_r8int5.py` | `4f10727d0c9b6788b4b42eb5adc4aa0a66a740aed9810aa4127e7f4379d9b77b` | 1095 | the r8int5 integrator (`rebind_current_evidence_r8int5.py`) | the docs(evidence) commit of `fnd/r8int5` |
| `r8int5/render_group1.py` | `bc2126969fb00925c9ce6b52ca29e46f5af35c4216cc0ecb337125fc57103be6` | 482 | the r8int5 integrator (`render_group1.py`) | the docs(evidence) commit of `fnd/r8int5` |
| `r8int5/s47_fix_r8int5.py` | `daf263c35f5b3f31dcd177ddb08fbb35c39b6b598d28677acfb4cba9f120a422` | 1471 | the r8int5 integrator (`s47_fix_r8int5.py`) | the docs(evidence) commit of `fnd/r8int5` |
| `r8int6/commit_r8int6.sh` | `b57498d0a6d6ac0d25701c7a812cb5287b941a1dfc7c5fe0d5fe475f41d056e0` | 1069 | the r8int6 integrator (`commit_r8int6.sh`); re-pinned 30 September 2026 by the scrub (`scrub/apply_scrub.py`): a path it named is derived now, and the bytes as filed are sha256 `cf2965e97ef4cbf4bc09787117faa70ff02a9628049b9e7a0f6f1ec2db12c23e`, 1018 bytes, in history at `8fec0733` | the set 6 commits; LAYER-STATUS.md's set 6 lines; V2-SPEC.md correction 31 |
| `r8int6/common/audit_diff_r8int6.py` | `0593bcf0981a3112ab5741b971a12e155ccc353b89e4843fc6e9c22d0879ff18` | 1551 | the r8int6 integrator (`common/audit_diff_r8int6.py`) | the set 6 commits; LAYER-STATUS.md's set 6 lines; V2-SPEC.md correction 31 |
| `r8int6/common/file_stream_r8int6.py` | `97937af44e688044137d9bb418535c1507e07a694c85e332db5960b743eeb9e9` | 1848 | the r8int6 integrator (`common/file_stream_r8int6.py`) | the set 6 commits; LAYER-STATUS.md's set 6 lines; V2-SPEC.md correction 31 |
| `r8int6/common/fill_msg_r8int6.py` | `c7833e67acb629be54e8a35489908501590826950987ae57b1297268eecabca8` | 690 | the r8int6 integrator (`common/fill_msg_r8int6.py`) | the set 6 commits; LAYER-STATUS.md's set 6 lines; V2-SPEC.md correction 31 |
| `r8int6/common/indep_r8int6.sh` | `7f005fed65463ac26951eb66918af6568cb48cb3f2693a3f14a4d0d35a6c7096` | 2027 | the r8int6 integrator (`common/indep_r8int6.sh`) | the set 6 commits; LAYER-STATUS.md's set 6 lines; V2-SPEC.md correction 31 |
| `r8int6/common/record_ids_r8int6.py` | `d1ccbd919ae3b4762511455e767942c0f0cb0c7d477fe58cd221b01d3ef5c3f1` | 3217 | the r8int6 integrator (`common/record_ids_r8int6.py`) | the set 6 commits; LAYER-STATUS.md's set 6 lines; V2-SPEC.md correction 31 |
| `r8int6/copy_evidence.sh` | `a9fae631c42eb945458c881c02131f9c339959e8396cc757e312f622513247ed` | 791 | the r8int6 integrator (`copy_evidence.sh`); re-pinned 30 September 2026 by the scrub (`scrub/apply_scrub.py`): a path it named is derived now, and the bytes as filed are sha256 `8bb596ad8eb75d009ff8a3b42e379784053cc43c2d2105fd608177528bd32e7d`, 746 bytes, in history at `8fec0733` | the set 6 commits; LAYER-STATUS.md's set 6 lines; V2-SPEC.md correction 31 |
| `r8int6/evidence-phase/audit-diff.txt` | `c8424e57601e487a6ac7fb102b8d34a87d27d93a4c3c482ba9602af00aec9f0e` | 7552 | the r8int6 integrator (`evidence-phase/audit-diff.txt`) | the set 6 evidence commit; CON-010's and REQ-044's rebind |
| `r8int6/evidence-phase/claims_check-retake.log` | `4518df05a5bf9733e9b778ecdacaff23463761bca3616129f11022dbce272cd0` | 300 | the r8int6 integrator (`evidence-phase/claims_check-retake.log`) | the set 6 evidence commit; CON-010's and REQ-044's rebind |
| `r8int6/evidence-phase/copy-evidence.log` | `d09911d0ed2df1815e4aa8a882fa300917583b6302eaa3dad0c198c8cdf0b3c4` | 109 | the r8int6 integrator (`evidence-phase/copy-evidence.log`) | the set 6 evidence commit; CON-010's and REQ-044's rebind |
| `r8int6/evidence-phase/evidence-head.txt` | `125776ca5613ec6fadfc48587632fee8b375e18b9f798df395b683ac9f82a2a2` | 46 | the r8int6 integrator (`evidence-phase/evidence-head.txt`) | the set 6 evidence commit; CON-010's and REQ-044's rebind |
| `r8int6/evidence-phase/render-1.log` | `fe9addc496ca91ac4fb104889f6ea4b537fc0abb72b8aa9d3ef7f5cea83eb77d` | 505 | the r8int6 integrator (`evidence-phase/render-1.log`) | the set 6 evidence commit; CON-010's and REQ-044's rebind |
| `r8int6/evidence-phase/render-2.log` | `e3b0c44298fc1c149afbf4c8996fb92427ae41e4649b934ca495991b7852b855` | 0 | the r8int6 integrator (`evidence-phase/render-2.log`) | the set 6 evidence commit; CON-010's and REQ-044's rebind |
| `r8int6/evidence-phase/status-1.log` | `96a2cacd73f5f947f07ffae7cf8b3a892bb5c1cf6a89c08f8c56805368265208` | 4067 | the r8int6 integrator (`evidence-phase/status-1.log`) | the set 6 evidence commit; CON-010's and REQ-044's rebind |
| `r8int6/evidence-phase/status-2.log` | `514916dc949f8757a591ee05b16c1ffb1531b822a573635b3d009a140a706702` | 4069 | the r8int6 integrator (`evidence-phase/status-2.log`) | the set 6 evidence commit; CON-010's and REQ-044's rebind |
| `r8int6/evidence-phase/status-3.log` | `514916dc949f8757a591ee05b16c1ffb1531b822a573635b3d009a140a706702` | 4069 | the r8int6 integrator (`evidence-phase/status-3.log`) | the set 6 evidence commit; CON-010's and REQ-044's rebind |
| `r8int6/evidence_r8int6.sh` | `8a7bcdcd047806151d7e1e34393086541e5219e7cd01ffaef5a7f7831724ad4d` | 1245 | the r8int6 integrator (`evidence_r8int6.sh`) | the set 6 commits; LAYER-STATUS.md's set 6 lines; V2-SPEC.md correction 31 |
| `r8int6/final-regen/a/parity_bom.json` | `5145580aba2011e2b5f33bb043e39677356bff43fef0c69f62fa928d20950422` | 68 | the r8int6 integrator (`final-regen/a/parity_bom.json`) | the set 6 commits; LAYER-STATUS.md's set 6 lines; V2-SPEC.md correction 31 |
| `r8int6/final-regen/a/parity_erc.json` | `0a2c44151af1c9dad222305680437412aee13d7633ab473c877079ffc1fe8298` | 359 | the r8int6 integrator (`final-regen/a/parity_erc.json`) | the set 6 commits; LAYER-STATUS.md's set 6 lines; V2-SPEC.md correction 31 |
| `r8int6/final-regen/a/parity_intent.json` | `607f2e1b7adb75dc66267217a7334114126f37ea6ca8cab0548736b90c1ba3d4` | 76 | the r8int6 integrator (`final-regen/a/parity_intent.json`) | the set 6 commits; LAYER-STATUS.md's set 6 lines; V2-SPEC.md correction 31 |
| `r8int6/final-regen/a/parity_netlist.json` | `6e4c415286caf00d71aa8ae74ef7022889ae6ae15afb71ef554fe72ada2dcdbd` | 751 | the r8int6 integrator (`final-regen/a/parity_netlist.json`) | the set 6 commits; LAYER-STATUS.md's set 6 lines; V2-SPEC.md correction 31 |
| `r8int6/final-regen/a/parity_schematic.json` | `785d0297dafc79b7c6f22f72f9b4f0106e23bd314dce674116c445fcafa4fe70` | 351 | the r8int6 integrator (`final-regen/a/parity_schematic.json`) | the set 6 commits; LAYER-STATUS.md's set 6 lines; V2-SPEC.md correction 31 |
| `r8int6/final-regen/a/regen-pcb-a-power.net.prov.json` | `c88fcba063f8bc3068bdcee753902cf18ad0c6ebc037453f4aef485a6c7d40c2` | 8641 | the r8int6 integrator (`final-regen/a/regen-pcb-a-power.net.prov.json`) | the set 6 commits; LAYER-STATUS.md's set 6 lines; V2-SPEC.md correction 31 |
| `r8int6/final-regen/a/regen.json` | `c898cc02add6542c9aa3bcf7dc87f8d3c2a87d0bc5b409c5defbd83d9063bb61` | 4768 | the r8int6 integrator (`final-regen/a/regen.json`) | the set 6 commits; LAYER-STATUS.md's set 6 lines; V2-SPEC.md correction 31 |
| `r8int6/final-regen/b/parity_bom.json` | `03f465eddadbfd91dd26942d4b8fdbf455dec01a469906a3b883524b77d89146` | 68 | the r8int6 integrator (`final-regen/b/parity_bom.json`) | the set 6 commits; LAYER-STATUS.md's set 6 lines; V2-SPEC.md correction 31 |
| `r8int6/final-regen/b/parity_erc.json` | `709898426c2bd634cf9ae66bc103da31ef20675bcbcd3a3c5fa43b16e70ecf6e` | 485 | the r8int6 integrator (`final-regen/b/parity_erc.json`) | the set 6 commits; LAYER-STATUS.md's set 6 lines; V2-SPEC.md correction 31 |
| `r8int6/final-regen/b/parity_intent.json` | `607f2e1b7adb75dc66267217a7334114126f37ea6ca8cab0548736b90c1ba3d4` | 76 | the r8int6 integrator (`final-regen/b/parity_intent.json`) | the set 6 commits; LAYER-STATUS.md's set 6 lines; V2-SPEC.md correction 31 |
| `r8int6/final-regen/b/parity_netlist.json` | `1ff0267356455da15c853f786368646a920f85e5608395ca647ab2f1ed983396` | 758 | the r8int6 integrator (`final-regen/b/parity_netlist.json`) | the set 6 commits; LAYER-STATUS.md's set 6 lines; V2-SPEC.md correction 31 |
| `r8int6/final-regen/b/parity_schematic.json` | `ae0669e008778caeef8abacf82b910c30b6718d65ac96ed67c81e066696088a0` | 351 | the r8int6 integrator (`final-regen/b/parity_schematic.json`) | the set 6 commits; LAYER-STATUS.md's set 6 lines; V2-SPEC.md correction 31 |
| `r8int6/final-regen/b/regen-pcb-b-compute.net.prov.json` | `a72788552bc692a4a8a4526a49c69d110567abd021fdd99a1820e017f0740293` | 8643 | the r8int6 integrator (`final-regen/b/regen-pcb-b-compute.net.prov.json`) | the set 6 commits; LAYER-STATUS.md's set 6 lines; V2-SPEC.md correction 31 |
| `r8int6/final-regen/b/regen.json` | `d645feacc8ef061d3aaa243846f7fb3cb9dc796bf175da771127a513ff6385c9` | 5892 | the r8int6 integrator (`final-regen/b/regen.json`) | the set 6 commits; LAYER-STATUS.md's set 6 lines; V2-SPEC.md correction 31 |
| `r8int6/final-regen/c/parity_bom.json` | `ac03074bb8ff1fffe5547d6fdb0d54c7f6a0b011a00e943d7b2725ac58278cfd` | 66 | the r8int6 integrator (`final-regen/c/parity_bom.json`) | the set 6 commits; LAYER-STATUS.md's set 6 lines; V2-SPEC.md correction 31 |
| `r8int6/final-regen/c/parity_erc.json` | `0e3856a43125518bd158e628baa35a1ca888a994531ff4773d5b06855f997eeb` | 353 | the r8int6 integrator (`final-regen/c/parity_erc.json`) | the set 6 commits; LAYER-STATUS.md's set 6 lines; V2-SPEC.md correction 31 |
| `r8int6/final-regen/c/parity_intent.json` | `607f2e1b7adb75dc66267217a7334114126f37ea6ca8cab0548736b90c1ba3d4` | 76 | the r8int6 integrator (`final-regen/c/parity_intent.json`) | the set 6 commits; LAYER-STATUS.md's set 6 lines; V2-SPEC.md correction 31 |
| `r8int6/final-regen/c/parity_netlist.json` | `be88efd29e448ba7c0304f6fef042129ce921e3773cde4a47e81c7d897cda459` | 756 | the r8int6 integrator (`final-regen/c/parity_netlist.json`) | the set 6 commits; LAYER-STATUS.md's set 6 lines; V2-SPEC.md correction 31 |
| `r8int6/final-regen/c/parity_schematic.json` | `617940d8a980b70f68f9536ef8497ba278c473abf190ae68e4d74776e69fa6ce` | 347 | the r8int6 integrator (`final-regen/c/parity_schematic.json`) | the set 6 commits; LAYER-STATUS.md's set 6 lines; V2-SPEC.md correction 31 |
| `r8int6/final-regen/c/regen-pcb-c-display.net.prov.json` | `e304d023fbf9e79c9c479eae0a07542d8dab71ac31180cb2b9a3ada2ecb63af4` | 8589 | the r8int6 integrator (`final-regen/c/regen-pcb-c-display.net.prov.json`) | the set 6 commits; LAYER-STATUS.md's set 6 lines; V2-SPEC.md correction 31 |
| `r8int6/final-regen/c/regen.json` | `a84898336f6d1f64d19a1e2ace6197addd2cb6db5128ddfff248f0b1b6ef1f08` | 3678 | the r8int6 integrator (`final-regen/c/regen.json`) | the set 6 commits; LAYER-STATUS.md's set 6 lines; V2-SPEC.md correction 31 |
| `r8int6/final-regen/d/parity_bom.json` | `38a45a536d61f86d91b1ac10e9c8e865434582cdf930f8240588b3f8457a9509` | 66 | the r8int6 integrator (`final-regen/d/parity_bom.json`) | the set 6 commits; LAYER-STATUS.md's set 6 lines; V2-SPEC.md correction 31 |
| `r8int6/final-regen/d/parity_erc.json` | `360922074f67148628c93519ed75a6c9f9690e98a268f08800c9511596d34cd6` | 353 | the r8int6 integrator (`final-regen/d/parity_erc.json`) | the set 6 commits; LAYER-STATUS.md's set 6 lines; V2-SPEC.md correction 31 |
| `r8int6/final-regen/d/parity_intent.json` | `607f2e1b7adb75dc66267217a7334114126f37ea6ca8cab0548736b90c1ba3d4` | 76 | the r8int6 integrator (`final-regen/d/parity_intent.json`) | the set 6 commits; LAYER-STATUS.md's set 6 lines; V2-SPEC.md correction 31 |
| `r8int6/final-regen/d/parity_netlist.json` | `059d5e61746a3bbba933c686a4fd18a31a31f2fedc4598f59854c3fafc63353a` | 747 | the r8int6 integrator (`final-regen/d/parity_netlist.json`) | the set 6 commits; LAYER-STATUS.md's set 6 lines; V2-SPEC.md correction 31 |
| `r8int6/final-regen/d/parity_schematic.json` | `af98d012beb62c3341802f374720616c5c84b954b3ae08ed8dfdd133fac5dc32` | 349 | the r8int6 integrator (`final-regen/d/parity_schematic.json`) | the set 6 commits; LAYER-STATUS.md's set 6 lines; V2-SPEC.md correction 31 |
| `r8int6/final-regen/d/regen-pcb-d-aprs.net.prov.json` | `2b33b172cfdb8b15a1ee243033f531e2cf66ec3407c969dbf66863c012f7c0d4` | 8640 | the r8int6 integrator (`final-regen/d/regen-pcb-d-aprs.net.prov.json`) | the set 6 commits; LAYER-STATUS.md's set 6 lines; V2-SPEC.md correction 31 |
| `r8int6/final-regen/d/regen.json` | `2b6c34a3016984a7f42fc4f7e844bb1c5ee4ae4f5eb103b3d910a0502b2a250f` | 5308 | the r8int6 integrator (`final-regen/d/regen.json`) | the set 6 commits; LAYER-STATUS.md's set 6 lines; V2-SPEC.md correction 31 |
| `r8int6/final-regen/e/parity_bom.json` | `4b3097655bf663177985428b8fda28e7e48409cdbadcab72076fc20db05cccf2` | 68 | the r8int6 integrator (`final-regen/e/parity_bom.json`) | the set 6 commits; LAYER-STATUS.md's set 6 lines; V2-SPEC.md correction 31 |
| `r8int6/final-regen/e/parity_erc.json` | `b6c52f4aaefee78154b5d74e1675408cef8fe524fb25171cfa4bce9dcc659b7a` | 353 | the r8int6 integrator (`final-regen/e/parity_erc.json`) | the set 6 commits; LAYER-STATUS.md's set 6 lines; V2-SPEC.md correction 31 |
| `r8int6/final-regen/e/parity_intent.json` | `607f2e1b7adb75dc66267217a7334114126f37ea6ca8cab0548736b90c1ba3d4` | 76 | the r8int6 integrator (`final-regen/e/parity_intent.json`) | the set 6 commits; LAYER-STATUS.md's set 6 lines; V2-SPEC.md correction 31 |
| `r8int6/final-regen/e/parity_netlist.json` | `10fad73d89b1509c8374190a1ad336649ee13d92ad9a9e5e56d9620f3651dea1` | 751 | the r8int6 integrator (`final-regen/e/parity_netlist.json`) | the set 6 commits; LAYER-STATUS.md's set 6 lines; V2-SPEC.md correction 31 |
| `r8int6/final-regen/e/parity_schematic.json` | `ace929ea68219b80b5988bb0d9b42f9a99b6fdda1b7305c112faa594f6a07d7d` | 349 | the r8int6 integrator (`final-regen/e/parity_schematic.json`) | the set 6 commits; LAYER-STATUS.md's set 6 lines; V2-SPEC.md correction 31 |
| `r8int6/final-regen/e/regen-pcb-e1-dock.net.prov.json` | `dacceb2ef2d4cc74bcba62df8e15a3e34d6dfc51023643a6bfb341932757ca21` | 8587 | the r8int6 integrator (`final-regen/e/regen-pcb-e1-dock.net.prov.json`) | the set 6 commits; LAYER-STATUS.md's set 6 lines; V2-SPEC.md correction 31 |
| `r8int6/final-regen/e/regen.json` | `ea3d86a9761104bb9e129d3d6f2a6c8fcf01837c0e406bea2bf2982f6972b3ff` | 4943 | the r8int6 integrator (`final-regen/e/regen.json`) | the set 6 commits; LAYER-STATUS.md's set 6 lines; V2-SPEC.md correction 31 |
| `r8int6/final-regen/p/parity_bom.json` | `dd8b22c8a83c901059522ce940b8cb9372084818c5a7eb6376c333fd5f0bc61b` | 66 | the r8int6 integrator (`final-regen/p/parity_bom.json`) | the set 6 commits; LAYER-STATUS.md's set 6 lines; V2-SPEC.md correction 31 |
| `r8int6/final-regen/p/parity_erc.json` | `34f41179c424a3f21c7f0b2fb0cab1e47b85bdc1a737f6965d9515ed58e9fc77` | 281 | the r8int6 integrator (`final-regen/p/parity_erc.json`) | the set 6 commits; LAYER-STATUS.md's set 6 lines; V2-SPEC.md correction 31 |
| `r8int6/final-regen/p/parity_intent.json` | `607f2e1b7adb75dc66267217a7334114126f37ea6ca8cab0548736b90c1ba3d4` | 76 | the r8int6 integrator (`final-regen/p/parity_intent.json`) | the set 6 commits; LAYER-STATUS.md's set 6 lines; V2-SPEC.md correction 31 |
| `r8int6/final-regen/p/parity_netlist.json` | `1331dc014a5ac1a34dfcb92860f66320b9a31ab43c6115cead4f54fb68f46b8b` | 743 | the r8int6 integrator (`final-regen/p/parity_netlist.json`) | the set 6 commits; LAYER-STATUS.md's set 6 lines; V2-SPEC.md correction 31 |
| `r8int6/final-regen/p/parity_schematic.json` | `f466f68f3e846502aa2ed1a2474c0294577ce676326e266ae941e3725e161453` | 345 | the r8int6 integrator (`final-regen/p/parity_schematic.json`) | the set 6 commits; LAYER-STATUS.md's set 6 lines; V2-SPEC.md correction 31 |
| `r8int6/final-regen/p/regen-pcb-p-pack.net.prov.json` | `580f16bbc70e4847d3c9fa409f8f10fa29797083a856a0571b6a9280bb081bf3` | 8640 | the r8int6 integrator (`final-regen/p/regen-pcb-p-pack.net.prov.json`) | the set 6 commits; LAYER-STATUS.md's set 6 lines; V2-SPEC.md correction 31 |
| `r8int6/final-regen/p/regen.json` | `74e08b3ecfc4a1466324e6c92670f05f7a113908b0f1527060c90fa3c5fe11f4` | 4720 | the r8int6 integrator (`final-regen/p/regen.json`) | the set 6 commits; LAYER-STATUS.md's set 6 lines; V2-SPEC.md correction 31 |
| `r8int6/final-regen/regen.log` | `49ad7c8f338cd4fc3f6b33e444f2685f41daf317df074929f86b43fab06efbc4` | 1401 | the r8int6 integrator (`final-regen/regen.log`) | the set 6 commits; LAYER-STATUS.md's set 6 lines; V2-SPEC.md correction 31 |
| `r8int6/indep/cmp-a.txt` | `1f83168af579a880730aba67e325773f304897f02d0ee0b3956c3ca1c2bf6313` | 767 | the r8int6 integrator (`indep/cmp-a.txt`) | the set 6 commits; LAYER-STATUS.md's set 6 lines; V2-SPEC.md correction 31 |
| `r8int6/indep/cmp-b.txt` | `d6a6e655f9d15e1937eef03560ccbc9f403dedfa889259210b715fdc08452f28` | 77 | the r8int6 integrator (`indep/cmp-b.txt`) | the set 6 commits; LAYER-STATUS.md's set 6 lines; V2-SPEC.md correction 31 |
| `r8int6/indep/cmp-c.txt` | `981e97c336a9fcd2dc9db7ca298be20fc32dd3336d622394a0d3bd16e2fddde2` | 2371 | the r8int6 integrator (`indep/cmp-c.txt`) | the set 6 commits; LAYER-STATUS.md's set 6 lines; V2-SPEC.md correction 31 |
| `r8int6/indep/cmp-d.txt` | `787acecf3e4cf89f57a1063a380b45f492df8544ff44d9e9b4ec010453d41290` | 288 | the r8int6 integrator (`indep/cmp-d.txt`) | the set 6 commits; LAYER-STATUS.md's set 6 lines; V2-SPEC.md correction 31 |
| `r8int6/indep/cmp-e.txt` | `6716a9a99c597a50c4bf82ae554d91de72bf60aab54db89c273712cb409604ee` | 1073 | the r8int6 integrator (`indep/cmp-e.txt`) | the set 6 commits; LAYER-STATUS.md's set 6 lines; V2-SPEC.md correction 31 |
| `r8int6/indep/cmp-p.txt` | `c9e5c2d5a265756e367b0211c64eb656518a99976b130f8e1e3e1b2432c36f51` | 204 | the r8int6 integrator (`indep/cmp-p.txt`) | the set 6 commits; LAYER-STATUS.md's set 6 lines; V2-SPEC.md correction 31 |
| `r8int6/indep/summary.txt` | `019a5cd3d1e661795d2a32737702e298422a5fd8918ff2ed0563062212bcb87a` | 1686 | the r8int6 integrator (`indep/summary.txt`) | the set 6 commits; LAYER-STATUS.md's set 6 lines; V2-SPEC.md correction 31 |
| `r8int6/kitprep_r8int6.sh` | `0533810c07aa0cadb88b58e59b8a5cf02b782f3c4cc9442d4120d26d501c9b69` | 398 | the r8int6 integrator (`kitprep_r8int6.sh`) | the set 6 commits; LAYER-STATUS.md's set 6 lines; V2-SPEC.md correction 31 |
| `r8int6/layers_r8int6.py` | `10971e29f81b5e648fe9c9958b19d6045191932a17365860714eda417799bed1` | 11646 | the r8int6 integrator (`layers_r8int6.py`) | the set 6 commits; LAYER-STATUS.md's set 6 lines; V2-SPEC.md correction 31 |
| `r8int6/r8int6_box.sh` | `50e8afb266b28f6e5c47fd8457348fe31375c55dbb87cd1027911da0649b04ac` | 932 | the r8int6 integrator (`r8int6_box.sh`) | the set 6 commits; LAYER-STATUS.md's set 6 lines; V2-SPEC.md correction 31 |
| `r8int6/r8int6_suite.sh` | `b7bad68131220e794764b9cf27ac12af9961fa76facb1ad07bc3dc90f7f0d7a6` | 798 | the r8int6 integrator (`r8int6_suite.sh`) | the set 6 commits; LAYER-STATUS.md's set 6 lines; V2-SPEC.md correction 31 |
| `r8int6/rebind_current_evidence_r8int6.py` | `c13072744d4259af16fd6ab949ec9683d39d75b7157921d2863f00fe42eb089c` | 3253 | the r8int6 integrator (`rebind_current_evidence_r8int6.py`) | the set 6 commits; LAYER-STATUS.md's set 6 lines; V2-SPEC.md correction 31 |
| `r8int6/stream_r8int6.sh` | `6d5326ce026526dd19a9eac123e3c81e469fc9f8ac57d0651000b2e2f485412f` | 731 | the r8int6 integrator (`stream_r8int6.sh`) | the set 6 commits; LAYER-STATUS.md's set 6 lines; V2-SPEC.md correction 31 |
| `r8int6/validate.sh` | `06b60404059afd6eea8aab82a7a47cdc9ac9df9d4e658b0c585e08a94ed98d51` | 601 | the r8int6 integrator (`validate.sh`) | the set 6 commits; LAYER-STATUS.md's set 6 lines; V2-SPEC.md correction 31 |
| `r8p/box/p1p2.txt` | `646d9a381f5eb076fa9b6012cdf7864c5f4f224ea2bc6b950b35c334b09f6b4f` | 2293 | `fnd/r8p` `drafts/p/box/p1p2.txt` | `v2/ecad/tools/pcb_requirements.yaml` (REQ-044) |
| `r8p/box/par.txt` | `31644e678a7e539a1783cdba34655d9ae96d85ab80fd7b82f1c634b82d07fbd5` | 3115 | `fnd/r8p` `drafts/p/box/par.txt` | `v2/ecad/tools/pcb_requirements.yaml` (REQ-044, CFL-015, CFL-016, CON-016) |
| `r8p/evidence/asked-Keystone_3568.txt` | `519f23ee3d8ffe0721c842337b0f41d41e80b77e9868c250fc839a2c5c35f45a` | 21 | `fnd/r8p` `drafts/p/evidence/asked-Keystone_3568.txt` | `v2/vendor/SOURCES.yaml` (pack-blade-fuse-holder) |
| `r8p/evidence/jlc-Keystone_3568.json` | `0959de51a5f57256dfd3f3f8ce7083914d5d2bb64fdcec6a3ec1dee56e7cb59e` | 12422 | `fnd/r8p` `drafts/p/evidence/jlc-Keystone_3568.json` | `v2/vendor/SOURCES.yaml` (pack-blade-fuse-holder) |
| `rel2/apply_registry.py` | `603b5cdbc92bdc911ad09e356d7524ec189e027acbb7852d2ff2b9125a0f44d2` | 29263 | `fnd/rel2` (authored in the tree by the second release attempt of layers 1 to 3) | `v2/ecad/tools/pcb_requirements.yaml` (its header); `v2/docs/handover/LAYER-STATUS.md` (layer 3) |
| `rel2/edit_docs.py` | `043f097b41731c8c2b328d71ba3e427cdfd28e47c2502cecc48e4b12e7669baf` | 45117 | `fnd/rel2` (authored in the tree by the second release attempt of layers 1 to 3) | the second release attempt's commit (`v2/docs/handover/LAYER-STATUS.md`, its paragraph and layers 1 and 2) |
| `rel2/edit_handover.py` | `80b94784aedd915c0cc160fbb111b912787368077dcd657c306b974299774ed1` | 12398 | `fnd/rel2` (authored in the tree by the second release attempt of layers 1 to 3) | `v2/docs/handover/LAYER-STATUS.md` (its paragraph and the integrator lines of layers 1 to 5) |
| `rel2/file_records.py` | `0e0bb35b14130472a2f8da4789e8e30b1e74cfe875c834a974cb1e334a3191be` | 5075 | `fnd/rel2` (authored in the tree by the second release attempt of layers 1 to 3) | this README's rows for `rel2/` and for the two review files |
| `rel2/post_docs_registry.py` | `4a353cad52ca0626d2b1a332903db52040d3b61e9b1dd18022dbc2edff0b651a` | 10853 | `fnd/rel2` (authored in the tree by the second release attempt of layers 1 to 3) | `v2/docs/handover/LAYER-STATUS.md` (layer 2); `v2/ecad/tools/pcb_requirements.yaml` (fifteen rebinds and the needs pin), `pcb_envelope.yaml`, `pcb_rules_coverage.yaml` (ENV-001) |
| `rel2/rebind_current_evidence.py` | `228d5271b4302b8029661b0fdb08a901f17f3ee63b6d89b6ad5e42ffd7893a6f` | 3202 | `fnd/rel2` (authored in the tree by the second release attempt of layers 1 to 3) | `v2/ecad/tools/pcb_requirements.yaml` (CON-010 and REQ-044 after the render) |
| `rel2/tool_compat.out` | `6542385d47ca74727d7a984f9c96d894a622c3c0516995ac171e26d8e43800fd` | 615 | `fnd/rel2` (authored in the tree by the second release attempt of layers 1 to 3) | `v2/docs/evidence/COMPATIBILITY.md` (the two tool entries of 27 September 2026) |
| `rel2/tool_compat.py` | `b9b8393c9a3c700b0790cdf2b14deea5c6f1810336ff4fe714f930977da6e94f` | 4975 | `fnd/rel2` (authored in the tree by the second release attempt of layers 1 to 3) | `v2/docs/evidence/COMPATIBILITY.md` (the two tool entries of 27 September 2026) |
| `rel2f/apply_compat.py` | `213fb3f787fe87149023e8bce92b93c022f20a71d873df388f3d5494819d0a5b` | 5465 | `fnd/rel2` (authored in the tree by the release finalizer of layers 1 to 3) | `v2/docs/evidence/COMPATIBILITY.md` (the third tool entry, `edge_length.py`, and its paragraph) |
| `rel2f/apply_registry.py` | `4e38fa32b695fd669a718508e5290acbcac691c2a0d39abab0c84261069daea9` | 8221 | `fnd/rel2` (authored in the tree by the release finalizer of layers 1 to 3) | `v2/ecad/tools/pcb_requirements.yaml` (its header and the three open items of the second release check) |
| `rel2f/check_rebase.py` | `fe4c0b4c46e7f9ca2b63c751f2662db4b6c77c55adf77d591574c0a817b4f5e4` | 2051 | `fnd/rel2` (authored in the tree by the release finalizer of layers 1 to 3) | the rebased second release attempt (`7dfbfb16`); `v2/docs/handover/LAYER-STATUS.md` (layer 2) |
| `rel2f/edit_docs.py` | `fa0ebae1f867858c5b410aadd09b7784bfbaef0a982718a1adb77216bfe4eccf` | 27490 | `fnd/rel2` (authored in the tree by the release finalizer of layers 1 to 3) | the finalizer's commit (`v2/docs/CONOPS.md`, `v2/docs/handover/LAYER-STATUS.md`, `ENGINEERING-QUESTIONS.md`, `START-HERE.md`) |
| `rel2f/file_records.py` | `9f4ba848599f0db2cb8a9b6ec0a6a6faec856e897f0e0a619323c505e6a33f83` | 5428 | `fnd/rel2` (authored in the tree by the release finalizer of layers 1 to 3) | this README's rows for `rel2f/` and for the three records of the second release check |
| `rel2f/ids.json` | `cacf7eb73e5c0ea3e265ee215caba2071158933774b4e8c69a2688ae6cb9f364` | 88 | `fnd/rel2` (authored in the tree by the release finalizer of layers 1 to 3) | `apply_registry.py` and `edit_docs.py` (the open item and question ids they took) |
| `rel2f/post_docs_registry.py` | `4fd5019002bd837cea5ae88d7a9633362128b6f8e179576c916db058d63d37c1` | 3094 | `fnd/rel2` (authored in the tree by the release finalizer of layers 1 to 3) | `v2/ecad/tools/pcb_requirements.yaml` (the needs pin and the three readings bound to CONOPS); `v2/docs/handover/LAYER-STATUS.md` (layer 2) |
| `rel2f/rebind_current_evidence.py` | `0a3bf702c7d10c6c6e4042174bc2cc62d59bdc66a59c9009f43d0f575712be59` | 2852 | `fnd/rel2` (authored in the tree by the release finalizer of layers 1 to 3) | `v2/ecad/tools/pcb_requirements.yaml` (CON-010 and REQ-044 after each render of the rebased branch) |
| `rel2f/resolve_rebase.py` | `6f5e87dd5a80e217de687ea545d7f351ab4cf75af75c44126bd453faf60d70d3` | 8299 | `fnd/rel2` (authored in the tree by the release finalizer of layers 1 to 3) | the rebased second release attempt (`7dfbfb16`, first rebased onto `391d8579`); `v2/docs/handover/LAYER-STATUS.md` (layers 2 and 3); ENGINEERING-QUESTIONS (the baseline question) |
| `rel2f/tool_compat_edge_length.out` | `5e772580d7347355b05e6f00eace9545c1efd7d7270a62e5c02c49972f756146` | 309 | `fnd/rel2` (authored in the tree by the release finalizer of layers 1 to 3) | `v2/docs/evidence/COMPATIBILITY.md` (the third tool entry) |
| `h2/apply_baseline.py` | `fc58460a6953d271c059955075c8c2f50330feecae1e68d42d99d1a1d1f1c415` | 10742 | `fnd/h2` (authored in the tree by the targeted fix of layers 1 and 3) | `v2/ecad/tools/pcb_requirements.yaml` (`baseline_state`, `baseline_reviews`, the header's paragraph on the baseline, S-51, S-77 and S-78 closed, S-79's title) |
| `h2/apply_verification.py` | `69eb6279602ee6b0c86a0cb28128e0710c0881c395130793dcada6e17598eb3b` | 12850 | `fnd/h2` (authored in the tree by the finalizer of the targeted fix, after its narrow verification) | `v2/ecad/tools/pcb_requirements.yaml` (`baseline_state` back to READY_FOR_REVIEW_B, the header's paragraph on the verification, S-51 and S-78 reopened, S-79's title, S-80 added, S-77's closing evidence) |
| `h2/box/box_exports.sh` | `461152acb346a6f8a6f9f47258d5d9110c1f6f85d76065799427e5a3b1b650bc` | 888 | `fnd/h2` (the H2 assembler's run on the rented KiCad box, filed byte for byte) | `v2/release/handover/_generated/` (the H2 exports of A, B, D and E) and `v2/docs/handover/REGENERATE.md` section 4 (the six-board regeneration) |
| `h2/box/ec_fetch.log` | `eebd117274e990d97de94cbeb2eef772b177feacab57360a0ebf61d5f5c4b1e3` | 2816 | `fnd/h2` (the H2 assembler's run on the rented KiCad box, filed byte for byte) | `v2/docs/handover/REGENERATE.md` section 6 (the chain with its one referenced citation restored) |
| `h2/box/ec_fetch.sh` | `ceb32b89ae20db60e22133426446fe3835ab584cd8675e9392220ed34c475037` | 1146 | `fnd/h2` (the H2 assembler's run on the rented KiCad box, filed byte for byte) | as for its log |
| `h2/box/exports.log` | `4a320d2241228d1c555a86efdc745c3e5e6a30fd3f4b0689ec5ec4a8a0970f1e` | 759 | `fnd/h2` (the H2 assembler's run on the rented KiCad box, filed byte for byte) | `v2/release/handover/_generated/` (the four re-exported boards) |
| `h2/box/regen.log` | `a43bc3cf0d93f34e9040670ebc234f1efc3438116ec465e668cbc3c974d16900` | 1425 | `fnd/h2` (the H2 assembler's run on the rented KiCad box, filed byte for byte) | `v2/docs/handover/REGENERATE.md` section 4 |
| `h2/box/section1a.log` | `c71ddafa5406a8ea282677f558f4c1a5046d0773b49cd4ddef966b814b9cf156` | 1653 | `fnd/h2` (the H2 assembler's run on the rented KiCad box, filed byte for byte) | `v2/docs/handover/REGENERATE.md` section 1a (run on the box as `ra2.sh`) |
| `h2/box/section1a.sh` | `60d7b68c3949a6f39f91a45ea24254270bae61a5a7cce430b073257de76f6123` | 1235 | `fnd/h2` (the H2 assembler's run on the rented KiCad box, filed byte for byte) | as for its log |
| `h2/box/zip_route.log` | `f5dd653db58b75c1d92c2f48b9df5f0f44c3d42c488f68e4a38541551ab0e8d3` | 20012 | `fnd/h2` (the H2 assembler's run on the rented KiCad box, filed byte for byte) | `v2/docs/handover/REGENERATE.md` sections 2 to 7 (the ZIP route of a build of H2 at `c5d09c78`; its section 1a is H1.1's wording, which H2 replaced) |
| `h2/box/zip_route.sh` | `94064990039479ef95942adb7ae6a662abc2dae8535e9121b9d43e460f33c7ee` | 5095 | `fnd/h2` (the H2 assembler's run on the rented KiCad box, filed byte for byte) | as for its log |
| `h2/handover_counts.out` | `b272b0ba740c7f9fd43e7ba74940698acbb14ad07ec24c89a72f66f164179d21` | 7036 | `fnd/h2` (authored in the tree by the H2 assembler) | every count of the H2 handover pages (START-HERE, LAYER-STATUS, CONTINUATION-BRIEF, ENGINEERING-QUESTIONS, REGENERATE); revised after H2 by the H2 minor-findings editor (`fnd/h2m`): the layout-entry labels printed whole, no count changed (H2's snapshot holds the version before, sha256 `9e41d27e1a76f7146e7b4a3357915626de0f7e8341d50851362f4c9fcfcbfd1a`) |
| `h2/handover_counts.py` | `9147dfc6a817436ded48b2e8da7b46f6d6218955bde9790ed900ac1f5b75f5d3` | 9364 | `fnd/h2` (authored in the tree by the H2 assembler) | as for its output; revised after H2 by the H2 minor-findings editor (`fnd/h2m`): the layout-entry labels printed whole, no count changed (H2's snapshot holds the version before, sha256 `c93087e914b93279a219ea568462802dcedd6fb6702ae3314d3ffd5b2cfaa638`) |
| `h2/registry_difference.out` | `a7424cf46db5e00edafadbf6b1a53a38b29392e43dfe026bc4538d2e374d2028` | 3095 | `fnd/h2` (authored in the tree by the targeted fix of layers 1 and 3) | `v2/ecad/tools/pcb_requirements.yaml` (the header's paragraphs on the targeted fix and the baseline; S-51 and S-78 closing evidence) |
| `h2/registry_difference.py` | `42568994b6ecf2bc199f7e83e11edd54665219941a22cbabbbc077fdee64a9e8` | 4626 | `fnd/h2` (authored in the tree by the targeted fix of layers 1 and 3) | `v2/ecad/tools/pcb_requirements.yaml` (as for its output) |
| `l3rb/apply_fix.py` | `33ea9fb5129ae110f61730305573d5a476e9b23b69d1e34acf6ade401c27556c` | 7734 | `fnd/l3rb` (authored in the tree by the re-baseline of layer 3) | `v2/ecad/tools/pcb_requirements.yaml` (CON-010's newest evidence entry, the header's paragraph on the targeted fix naming 79963b3b, the header's paragraph on the re-baseline, S-81 added) |
| `l3rb/apply_baseline.py` | `ca88d7e479f6250d55965e8459d6ba6e8e9cb68ae5b61cd5765441ef9617a7ce` | 18514 | `fnd/l3rb` (authored in the tree by the re-baseline of layer 3) | `v2/ecad/tools/pcb_requirements.yaml` (`baseline_state` BASELINED at `a54b793b`, `baseline_reviews` with the narrow verification, the header's paragraph on the baseline, again, S-51, S-78 and S-80 closed) |
| `l3rb/rebaseline_difference.out` | `d04f298f32e7c041df8bd66c8c44d2168d193c2ccce061f16531d0f16a187753` | 1690 | `fnd/l3rb` (authored in the tree by the re-baseline of layer 3) | `v2/ecad/tools/pcb_requirements.yaml` (the header's paragraph on the baseline, again; S-78's and S-80's closing evidence) |
| `l3rb/rebaseline_difference.py` | `5dbb546dd4c375b410ce90a045e94d1987e858282d14055d3f13957ad00af536` | 6857 | `fnd/l3rb` (authored in the tree by the re-baseline of layer 3) | `v2/ecad/tools/pcb_requirements.yaml` (as for its output) |
| `l3rb/apply_recheck.out` | `f4bbfde1ba909781184eb0172ebc56de2e8cfe1b4a25aa4b8c06ce78eb0385dd` | 221 | `fnd/l3rb` (authored in the tree by the finalizer of the re-check of layer 3's re-baseline) | `v2/ecad/tools/pcb_requirements.yaml` (the header's paragraph on the re-check) |
| `l3rb/apply_recheck.py` | `3123238b08d5282fbc92033990c25b61e10b1313dd199b2f6cbe01651b25dc9b` | 10462 | `fnd/l3rb` (authored in the tree by the finalizer of the re-check of layer 3's re-baseline) | `v2/ecad/tools/pcb_requirements.yaml` (the header's paragraph on the re-check, `baseline_reviews` with the re-check, the closing evidence of S-51, S-78 and S-80, S-79's title) |
| `l3rb/edit_docs.py` | `c590bf49c47b9ba8a775fe6f169a0a845fa0669acf95e0ddb6e7235f8c291965` | 15263 | `fnd/l3rb` (authored in the tree by the finalizer of the re-check of layer 3's re-baseline) | `v2/docs/handover/LAYER-STATUS.md` (layer 3 COMPLETE: the summary sentences, the H2 section's row, the integrator line); `v2/docs/handover/ENGINEERING-QUESTIONS.md` (EQ-28 and EQ-30 answered, EQ-29) |
| `h2m/h2m_layer_tables.py` | `d667d52bb5a91e505aa3380e633318f51146375d57426f322efd23997a087743` | 26476 | `fnd/h2m` (authored in the tree by the H2 minor-findings editor) | `v2/docs/handover/LAYER-STATUS.md` (each layer's acceptance table at H2 and Appendix A) |
| `h2m/box/repo_route.log` | `589fc12a3b8e188b3f2d9d058a7b95299dd30da4e7df98c9756bdbf839141a25` | 4914 | `fnd/h2m` (authored in the tree by the H2 minor-findings editor, the run on the rented KiCad box, filed byte for byte) | `v2/docs/handover/REGENERATE.md` sections 1a, 7 and 9 (the third route, board P's re-take, the validator's counts in a repository built from the ZIP) |
| `h2m/box/repo_route.sh` | `f0d05b1dbfca9005beaeb443d3cf69ba831cae67d06104356827a87d9150513a` | 4891 | `fnd/h2m` (authored in the tree by the H2 minor-findings editor, the run on the rented KiCad box, filed byte for byte) | as for its log |
| `h2m/box/retake-p.json` | `281f3166627e295119433c1498d7d2b90e7521eec17ebfc9c36436b8a273ce5b` | 17327 | `fnd/h2m` (authored in the tree by the H2 minor-findings editor, the run on the rented KiCad box, filed byte for byte) | `v2/docs/handover/REGENERATE.md` section 9 (board P's 14 readings) |
| `h2m/box/retake-p.log` | `0393b8700a9f8ab9513aa38aeeaa2686be02e7cd2ca315e807320fe923ffaed6` | 3555 | `fnd/h2m` (authored in the tree by the H2 minor-findings editor, the run on the rented KiCad box, filed byte for byte) | as for its JSON |
| `h3/apply_rebinds.out` | `1d4a6f22f86d99a2aa2efdf2213c4644d09c8d1ac52dc47e203fa0e149d33178` | 806 | `fnd/h3` (authored in the tree by the H3 pages worker) | as for its script |
| `h3/apply_rebinds.py` | `f58e4efde5ac4174ac5bc401227e213f74236cb1e6f147f7b215fc9152e9f5ae` | 12242 | `fnd/h3` (authored in the tree by the H3 pages worker) | no page: the check that no page edited for H3 is bound by the requirements registry, and the rebind path with its self-test |
| `h3/apply_records_readme.py` | `6351d4c3cb33eb38ee2877c0f104bfb4aab6af3b459015208d65327bb9c2959f` | 6115 | `fnd/h3` (authored in the tree by the H3 pages worker) | this README (the rows of `h3/`) |
| `h3/design_difference.out` | `b687163fd89a299b31893ad73ded5d0a890c76ce812100bf1c61a8b79f157316` | 9716 | `fnd/h3` (authored in the tree by the H3 pages worker) | as for its script |
| `h3/design_difference.py` | `834da59b801ac630e7760a411ebbd96d313cc16a57f0b9b7072f3884407ace67` | 15434 | `fnd/h3` (authored in the tree by the H3 pages worker) | `v2/docs/handover/START-HERE.md` section 1a, `LAYER-STATUS.md` (Status at handover H3), `REGENERATE.md` (Edition H3) and `RELEASE-H3.md`: H3's design content is H2's |
| `h3/handover_counts.out` | `d487511dce7ca09f3f8e9f9839f89431b37d1c64f1e0812cc36ea23836c7180b` | 7965 | `fnd/h3` (authored in the tree by the H3 pages worker) | as for its script |
| `h3/handover_counts.py` | `ae2706204a33f473b9ef808f861fcafbafa3cee26f9eea1d11fae2c2b0d6494c` | 11525 | `fnd/h3` (authored in the tree by the H3 pages worker) | every count of the H3 handover pages (START-HERE, LAYER-STATUS, CONTINUATION-BRIEF, ENGINEERING-QUESTIONS, REGENERATE, RELEASE-H3); a copy of `h2/handover_counts.py`, its docstring listing the four differences |
| `h3/public_check.out` | `ccc3ece5eaca499bd9f127ec9d7d1ed36dfdf378532af4955c65c79f843c64f3` | 2954 | `fnd/h3` (authored in the tree by the H3 pages worker) | as for its script |
| `h3/public_check.py` | `505a873ae67a0257bcf8afebe3c611baaa3e5da33e1ef29bcdfa64803296ad0b` | 5191 | `fnd/h3` (authored in the tree by the H3 pages worker) | `v2/docs/handover/REGENERATE.md` sections 7 and 9, `H2-RESPONSE.md` M1 and `RELEASE-H3.md`: which commits are on the public repository, asked at the time it prints |
| `h3/same_patches.out` | `9add3fd6ef73c7795f2bc469e25bbf59398125717c28a20a621cd41dc315ab02` | 3066 | `fnd/h3` (authored in the tree by the H3 pages worker) | as for its script |
| `h3/same_patches.py` | `02fb0f34013620c5ff06b758514bdb0333a31b339e1a50e2a10e8876d8be45c3` | 3359 | `fnd/h3` (authored in the tree by the H3 pages worker) | `v2/docs/handover/H2-RESPONSE.md` (the correction of the commit ids) and `REGENERATE.md` section 9 |
| `h3/zip_size_estimate.out` | `9b7899b1518835a87c47875c30745a48f6d5ab86d0a0f576a22a95015f1b8c29` | 3270 | `fnd/h3` (authored in the tree by the H3 pages worker) | as for its script |
| `h3/zip_size_estimate.py` | `a50b57094730b8a10aea323d6e03f86a88caa605b4449a258c92aa2b9f2e94fe` | 7515 | `fnd/h3` (authored in the tree by the H3 pages worker) | `v2/docs/handover/pack.yaml` (the comment on H3): the ZIP's expected size against `max_zip_bytes`, before the build |
| `rv-bat/bat-integration-notes.md` | `af4516bccc528c3e309a9237fa060357ac26961de499458f0b19a6f9f640bc5b` | 12303 | `fnd/rv-bat` `drafts/bat-integration-notes.md` | `v2/docs/review-packets/battery/MANIFEST.md` |
| `rv-bat/box/bat-cycle1/new/files/pcb-p-pack.net` | `4df605c1c9a9d2dbf17b4758cb1fe65205800668a19e30fb6f70b0daa1c4bfc4` | 91969 | `fnd/rv-bat` `drafts/box/bat-cycle1/new/files/pcb-p-pack.net` | `v2/docs/review-packets/battery/evidence/regeneration/test-pack-secondary-ts-runs.txt` |
| `rv-bat/box/bat-cycle1/new/files/pcb-p-pack.net.prov.json` | `e6fe22a3cc3df7d6d08c2a0de930d6de4a4eca1bc5e876bccf967717b3f95638` | 8498 | `fnd/rv-bat` `drafts/box/bat-cycle1/new/files/pcb-p-pack.net.prov.json` | `v2/docs/review-packets/battery/evidence/regeneration/test-pack-secondary-ts-runs.txt` |
| `rv-bat/box/bat-cycle1/run.log` | `9bffc3191029b7f528e42f8e9302f3d2b1ba00ad34a2ccfe0efafde5702d99e7` | 3548 | `fnd/rv-bat` `drafts/box/bat-cycle1/run.log` | `v2/docs/review-packets/battery/MANIFEST.md` |
| `rv-bat/box/bat/suite-worktree-cycle3.log` | `239a5d3e3d1fd06459627ce8bd081aecd534629520b50a16a9da1cca29cf7fec` | 153630 | `fnd/rv-bat` `drafts/box/bat/suite-worktree-cycle3.log` | `v2/docs/review-packets/battery/MANIFEST.md` |
| `rv-bat/box/bat/suite-worktree.log` | `b10fecd057ba0aff6bc53aad1a7e4d5cea3aee4c071177e08ddaf256aafc2629` | 153623 | `fnd/rv-bat` `drafts/box/bat/suite-worktree.log` | `v2/docs/review-packets/battery/MANIFEST.md` |
| `rv-bat/datasheets/SOURCES.txt` | `fa0399eb8bfcf2a9c9d0fb1a3bf9306836f6b6cd8194742a7fd5099d35d2e576` | 9648 | `fnd/rv-bat` `drafts/datasheets/SOURCES.txt` | `v2/docs/review-packets/battery/MANIFEST.md` |
| `rv-bat/vendor-files.txt` | `f3c546e124cc2b27f89dba24d7283e7329508a258642f3bcbceebcb4b33aac36` | 4272 | `fnd/rv-bat` `drafts/vendor-files.txt` | `v2/docs/review-packets/battery/MANIFEST.md` |
| `rv-dec/PCB-OPEN-PAIRS.decision-42.isolated.diff` | `1fc433e865bff5de41aa43fd8c0776821f58cb3e2f2698bf204b0a3ecd3b91fb` | 3703 | `fnd/rv-dec` `drafts/PCB-OPEN-PAIRS.decision-42.isolated.diff` | `v2/docs/feasibility/DECOUPLING.md` |
| `rv-dec/datasheets/SOURCES.txt` | `05deb9062aaf96f8092e1664cc4b9c84faa3db89543caf3eac0d1a3094144af7` | 1616 | `fnd/rv-dec` `drafts/datasheets/SOURCES.txt` | `v2/docs/feasibility/DECOUPLING.md` |
| `rv-dec/dec-request-diodes-pi7c9x2g404sl.md` | `3429e1ebdaec77d45c08c8ee82edf6884f4b46514723b8f8790bc1ea3472bf2c` | 1974 | `fnd/rv-dec` `drafts/dec-request-diodes-pi7c9x2g404sl.md` | `v2/docs/feasibility/DECOUPLING.md` |
| `rv-dec/dec_escset.out` | `1b6b5f7adda5e92d900d2100dbb5856b7d04c662fb97fbc2a0c13fa32aa1dad8` | 25200 | `fnd/rv-dec` `drafts/dec_escset.out` | `v2/docs/feasibility/DECOUPLING.md` |
| `rv-dec/dec_escset.py` | `14aa6aab298f8711873dbab4f3521cba2214bac886beb5c8a88503009f9412e1` | 3847 | `fnd/rv-dec` `drafts/dec_escset.py` | `v2/docs/feasibility/DECOUPLING.md` |
| `rv-dec/dec_escvias.out` | `18eb109b0761515e8f5fe5431ffb18c2c20c4ee3638eda014c4d35813b98330c` | 584 | `fnd/rv-dec` `drafts/dec_escvias.out` | `v2/docs/feasibility/DECOUPLING.md` |
| `rv-dec/dec_escvias.py` | `2a9c5f76e50565715d68490fe0310d457203d7929d534d004fdf1b0326f2652d` | 2168 | `fnd/rv-dec` `drafts/dec_escvias.py` | `v2/docs/feasibility/DECOUPLING.md` |
| `rv-dec/dec_fanwin.py` | `0db8b66f971b33c9220fe7112aa710ee9558492de3d9f323195a066f4d411167` | 3910 | `fnd/rv-dec` `drafts/dec_fanwin.py` | `v2/docs/feasibility/DECOUPLING.md` |
| `rv-dec/dec_farside.before-17h15.out` | `58bdc3b166bad755de3ee5382d23ba2e2cf8900a853fd6d14a33f1ff3bc96d45` | 9619 | `fnd/rv-dec` `drafts/dec_farside.before-17h15.out` | `v2/docs/feasibility/DECOUPLING.md` |
| `rv-dec/dec_farside.out` | `3173557d0cf6f590f365227d1a631edbaae9bd84cfc213517e8bd23b2cec45dd` | 9825 | `fnd/rv-dec` `drafts/dec_farside.out` | `v2/docs/feasibility/DECOUPLING.md` |
| `rv-dec/dec_farside.py` | `22d3ab7f5e12776341084e4e346b336ff7cb856755f1405bd3ad1dc8d545a14c` | 5114 | `fnd/rv-dec` `drafts/dec_farside.py` | `v2/docs/feasibility/DECOUPLING.md` |
| `rv-dec/dec_finesets.before-17h15.out` | `1f671a942967e4abd0aca55c71e3b413a08c58391a82ca5215f5c2d9a34c2a2c` | 291 | `fnd/rv-dec` `drafts/dec_finesets.before-17h15.out` | `v2/docs/feasibility/DECOUPLING.md` |
| `rv-dec/dec_finesets.out` | `3a4db397e9047965ae24e799ad3b45588ac74a5738b7eb30818b840bc04c5093` | 292 | `fnd/rv-dec` `drafts/dec_finesets.out` | `v2/docs/feasibility/DECOUPLING.md` |
| `rv-dec/dec_finesets.py` | `96069898ef19c835ef14a60c7b2b4bc4bae9c665f6ff45daffdc4a3b4b281ff4` | 1377 | `fnd/rv-dec` `drafts/dec_finesets.py` | `v2/docs/feasibility/DECOUPLING.md` |
| `rv-dec/dec_geom_pcb-a-power-a23.json` | `e9dbb38eaab141f271bea175966539cd5659d13f1672e14cdfe09f8fb3e78f9b` | 18862 | `fnd/rv-dec` `drafts/dec_geom_pcb-a-power-a23.json` | `v2/docs/feasibility/DECOUPLING.md` |
| `rv-dec/dec_geom_pcb-a-power-a23.txt` | `bdda040348795966c26060405f614438d2c1d8f1423d8da07fa70792fbbf8c53` | 7111 | `fnd/rv-dec` `drafts/dec_geom_pcb-a-power-a23.txt` | `v2/docs/feasibility/DECOUPLING.md` |
| `rv-dec/dec_geom_pcb-b-compute-b19.json` | `126e7667ff3dfe26e087c888d97e732645c4593f278aa06f64109a9cdb040c5e` | 17583 | `fnd/rv-dec` `drafts/dec_geom_pcb-b-compute-b19.json` | `v2/docs/feasibility/DECOUPLING.md` |
| `rv-dec/dec_geom_pcb-b-compute-b19.txt` | `0e54ea8e684e857bd04d1a5ac82cd85c1cc2a5ed3a49b740007c7757030c4028` | 6711 | `fnd/rv-dec` `drafts/dec_geom_pcb-b-compute-b19.txt` | `v2/docs/feasibility/DECOUPLING.md` |
| `rv-dec/dec_geom_pcb-c-display-c8.json` | `90e52bf8c6e969afa8ff20dba649936fcd1936e6cba7176b850c423a967b885f` | 10553 | `fnd/rv-dec` `drafts/dec_geom_pcb-c-display-c8.json` | `v2/docs/feasibility/DECOUPLING.md` |
| `rv-dec/dec_geom_pcb-c-display-c8.txt` | `37699f7ad0c6703fada5a57395f3362578ab36db33a9174ee70ace5ad9950e50` | 4065 | `fnd/rv-dec` `drafts/dec_geom_pcb-c-display-c8.txt` | `v2/docs/feasibility/DECOUPLING.md` |
| `rv-dec/dec_geom_pcb-d-aprs-d9.json` | `fb39a416968ae18a38a59faab04831f32c7dc05e8a05f9d319976038a5964897` | 13856 | `fnd/rv-dec` `drafts/dec_geom_pcb-d-aprs-d9.json` | `v2/docs/feasibility/DECOUPLING.md` |
| `rv-dec/dec_geom_pcb-d-aprs-d9.txt` | `c2b93acd520861403bbb7a0fbd6f134889d8f55df0d931e15f5d0e43ef3d3c6a` | 5444 | `fnd/rv-dec` `drafts/dec_geom_pcb-d-aprs-d9.txt` | `v2/docs/feasibility/DECOUPLING.md` |
| `rv-dec/dec_geom_pcb-e1-dock-e7.json` | `d94ee632c3204fc251d4514323d76e3ba108fe2580afe5b74f414a4c772e871f` | 10729 | `fnd/rv-dec` `drafts/dec_geom_pcb-e1-dock-e7.json` | `v2/docs/feasibility/DECOUPLING.md` |
| `rv-dec/dec_geom_pcb-e1-dock-e7.txt` | `f04d47c2f6181b0e8dd9334d4b6118fcf21c9a5788f79bd14921b6dc9a6b909f` | 4133 | `fnd/rv-dec` `drafts/dec_geom_pcb-e1-dock-e7.txt` | `v2/docs/feasibility/DECOUPLING.md` |
| `rv-dec/dec_geom_pcb-p-pack-p2.json` | `b6263d87a0aab0006fbca673192343e65c8f8516ca3cf5b1a93cd04dd3cf9a50` | 1848 | `fnd/rv-dec` `drafts/dec_geom_pcb-p-pack-p2.json` | `v2/docs/feasibility/DECOUPLING.md` |
| `rv-dec/dec_geom_pcb-p-pack-p2.txt` | `d2754f45088e73c16f967810bac1904324ae221b57f3986e940e4af6627d1505` | 708 | `fnd/rv-dec` `drafts/dec_geom_pcb-p-pack-p2.txt` | `v2/docs/feasibility/DECOUPLING.md` |
| `rv-dec/dec_geom_table.md` | `a485552f8f4162e57141596afaecfa52a9f9a95121c2f916d73f6f7cf2f14314` | 4281 | `fnd/rv-dec` `drafts/dec_geom_table.md` | `v2/docs/feasibility/DECOUPLING.md` |
| `rv-dec/dec_geometry.py` | `fc926ba59d982b6f109c99b5a72d6a8ea130ca1d6cdb8dd1c54d28e40671ee30` | 11642 | `fnd/rv-dec` `drafts/dec_geometry.py` | `v2/docs/feasibility/DECOUPLING.md` |
| `rv-dec/dec_loop.out` | `85dc41584ef9aaab3e5d1db5c3d5e26830cd60432709d01c8f78cb3a2b9c5f67` | 5158 | `fnd/rv-dec` `drafts/dec_loop.out` | `v2/docs/feasibility/DECOUPLING.md` |
| `rv-dec/dec_loop.py` | `eed91e6beb8b1fdb8de067667c434f799f20117c61c48ac08ef9633bf202c051` | 6319 | `fnd/rv-dec` `drafts/dec_loop.py` | `v2/docs/feasibility/DECOUPLING.md` |
| `rv-dec/dec_mmscan.err` | `e1f317bb966d63ee6869e9c744c6208a1807842953ff49082165d073b25f07ab` | 27 | `fnd/rv-dec` `drafts/dec_mmscan.err` | `v2/docs/feasibility/DECOUPLING.md` |
| `rv-dec/dec_mmscan.out` | `0ce71790d660874aee17670ae03be9f86f36e8c90733fd9bfd560863981b01a0` | 1628 | `fnd/rv-dec` `drafts/dec_mmscan.out` | `v2/docs/feasibility/DECOUPLING.md` |
| `rv-dec/dec_mmscan.py` | `4cba5432e38b426fac5bb4de458fb59079232a3a894d24ee4be1a0bae5d209bf` | 1601 | `fnd/rv-dec` `drafts/dec_mmscan.py` | `v2/docs/feasibility/DECOUPLING.md` |
| `rv-dec/dec_newfans.out` | `2c6e0e762020c71bdb62d872c1c93b1abda7515adac0d5b4b68910dfb294c4c3` | 1467 | `fnd/rv-dec` `drafts/dec_newfans.out` | `v2/docs/feasibility/DECOUPLING.md` |
| `rv-dec/dec_newfans.py` | `b7b8cf6284e7f17307322b74a5978f82434ce7e7accdacdb78b19edfe7621cde` | 2077 | `fnd/rv-dec` `drafts/dec_newfans.py` | `v2/docs/feasibility/DECOUPLING.md` |
| `rv-dec/dec_planes.out` | `11f7337a77ac81e091dde17e8121bf07196cfa8b5707620b1e036045bb6d10ca` | 4806 | `fnd/rv-dec` `drafts/dec_planes.out` | `v2/docs/feasibility/DECOUPLING.md` |
| `rv-dec/dec_planes.py` | `a6d0256b4ad8c8d2dece39f3dce98fd5354ea87db61b2dc40e815bcba1224479` | 1561 | `fnd/rv-dec` `drafts/dec_planes.py` | `v2/docs/feasibility/DECOUPLING.md` |
| `rv-dec/dec_sides.out` | `9fd3a9dc45c09e1a52cbcceb71f3bdd28bdd4fcbdd2321e2f6c5c509ccf33d60` | 40378 | `fnd/rv-dec` `drafts/dec_sides.out` | `v2/docs/feasibility/DECOUPLING.md` |
| `rv-dec/dec_sides.py` | `3730e4328f4d10411cdde4b3796cc3c3a470a568e6da519e6864e6c56c3fb15b` | 1991 | `fnd/rv-dec` `drafts/dec_sides.py` | `v2/docs/feasibility/DECOUPLING.md` |
| `rv-dec/dec_sides_decl.out` | `ab69cedf2f86fe58e10e17d0a5bdcd1a198f27030b8e2e5eacb00056a609da83` | 16961 | `fnd/rv-dec` `drafts/dec_sides_decl.out` | `v2/docs/feasibility/DECOUPLING.md` |
| `rv-dec/dec_sides_decl.py` | `a788a9365159eb57531b7d8126eda712b528eb1a6c46cedc750badf63ea47076` | 1583 | `fnd/rv-dec` `drafts/dec_sides_decl.py` | `v2/docs/feasibility/DECOUPLING.md` |
| `rv-emc/datasheets/SHA256SUMS` | `c911282e3cccf6b594cac97e03449d169fa0259680fb91b00f13a335fcb52961` | 1793 | `fnd/rv-emc` `drafts/datasheets/SHA256SUMS` | `v2/docs/feasibility/EMCON.md` |
| `rv-emc/datasheets/SOURCES.txt` | `e31f8043723f3e74c1662aaaee2286e4e80c10268c075c7c1bc530708869466e` | 4619 | `fnd/rv-emc` `drafts/datasheets/SOURCES.txt` | `v2/docs/feasibility/EMCON.md` |
| `rv-emc/netlists/A-r6cand-pcb-a-power.net` | `e7c50a4f212a510a7df37693bd600af64539b2f3077ef7cb8e96bb150beb96c5` | 592776 | `fnd/rv-emc` `drafts/netlists/A-r6cand-pcb-a-power.net` | `v2/docs/feasibility/EMCON.md` |
| `rv-emc/netlists/A-r6cand-pcb-a-power.net.prov.json` | `aadf6aea8234396188573205233cc052d0638a5301ac34bf7dd8651b226efc84` | 8499 | `fnd/rv-emc` `drafts/netlists/A-r6cand-pcb-a-power.net.prov.json` | `v2/docs/feasibility/EMCON.md` |
| `rv-emc/netlists/B-r6cand-pcb-b-compute.net.prov.json` | `4c1d9b2665324943f35830cb6161e0694c8178c98abcfba25e406d4472e2cd55` | 8501 | `fnd/rv-emc` `drafts/netlists/B-r6cand-pcb-b-compute.net.prov.json` | `v2/docs/feasibility/EMCON.md` |
| `rv-emc/netlists/D-r6cand-pcb-d-aprs.net` | `9aae5bf93a104abcbf14568657b79d11704cb243971415fd0bc0ac6911263a94` | 247232 | `fnd/rv-emc` `drafts/netlists/D-r6cand-pcb-d-aprs.net` | `v2/docs/feasibility/EMCON.md` |
| `rv-emc/netlists/D-r6cand-pcb-d-aprs.net.prov.json` | `71f4a2068f25c87a890070c617e67a724b59e800aabd77bab4e7dcde081e457f` | 8498 | `fnd/rv-emc` `drafts/netlists/D-r6cand-pcb-d-aprs.net.prov.json` | `v2/docs/feasibility/EMCON.md` |
| `rv-emc/netlists/SHA256SUMS` | `40d7131f3e0e932b9747c5f7c12fec93577acec1c9c16e603865697a1312fc3c` | 798 | `fnd/rv-emc` `drafts/netlists/SHA256SUMS` | `v2/docs/feasibility/EMCON.md` |
| `rv-emc/readings/A-nets.txt` | `0ca1600212a5bd2158048189dcacd05d2fb50385eefd3f084ef1670f9cbeeb5b` | 4132 | `fnd/rv-emc` `drafts/readings/A-nets.txt` | `v2/docs/feasibility/EMCON.md` |
| `rv-emc/readings/B-e22-e72.txt` | `4fdb45beef9332f93fe02634e4278d0cf6c3694f1526af491b47f6bfca9350c3` | 5864 | `fnd/rv-emc` `drafts/readings/B-e22-e72.txt` | `v2/docs/feasibility/EMCON.md` |
| `rv-emc/readings/B-m2c2-sdemc1.txt` | `72fdc8b2a92561cdaf70869cf9ce42791b4caa408150c09e695f95a591a744d0` | 11583 | `fnd/rv-emc` `drafts/readings/B-m2c2-sdemc1.txt` | `v2/docs/feasibility/EMCON.md` |
| `rv-emc/readings/B-nets-1.txt` | `8fe20f994c243e92c64af02e923a92fb326b9bcb63da6a32077056155f7d38d7` | 7718 | `fnd/rv-emc` `drafts/readings/B-nets-1.txt` | `v2/docs/feasibility/EMCON.md` |
| `rv-emc/readings/B-nets-cm5.txt` | `1858194cca83a4ad4c8c80ff81b36b8486949a200475e9e32e361c95bb200f00` | 3892 | `fnd/rv-emc` `drafts/readings/B-nets-cm5.txt` | `v2/docs/feasibility/EMCON.md` |
| `rv-emc/readings/B-nets-m2-io.txt` | `33e7527b2e34026b660e11269e6e7bb8e90be8711ad646390d90ad9f42bc6da3` | 9480 | `fnd/rv-emc` `drafts/readings/B-nets-m2-io.txt` | `v2/docs/feasibility/EMCON.md` |
| `rv-emc/readings/B-nets-m2.txt` | `1f46803581ebe2abfd160c77ed2c3a7e66f01eb4f4ed52309883cd78c154870a` | 4154 | `fnd/rv-emc` `drafts/readings/B-nets-m2.txt` | `v2/docs/feasibility/EMCON.md` |
| `rv-emc/readings/B-rb-lime.txt` | `b8b6f5a78c9d437bb747a5400de409411447e876dbb9f06d518a4f3f51f58e20` | 2062 | `fnd/rv-emc` `drafts/readings/B-rb-lime.txt` | `v2/docs/feasibility/EMCON.md` |
| `rv-emc/readings/B-refs-gates.txt` | `610dc419377e7d95f6b524fd4fbe4dc77c99cea15c137ae39eaefdee3bcbbb5d` | 2430 | `fnd/rv-emc` `drafts/readings/B-refs-gates.txt` | `v2/docs/feasibility/EMCON.md` |
| `rv-emc/readings/B-refs-m2.txt` | `6d646b7465fa33b8f5b88042074cb2e9db6150e297ccd6202fde3909b4ee7f19` | 1676 | `fnd/rv-emc` `drafts/readings/B-refs-m2.txt` | `v2/docs/feasibility/EMCON.md` |
| `rv-emc/readings/B-refs-pulls.txt` | `6bbcec8721bb8d82fd3a1cb4f020797725b8bec96de78c775bb3d8504dce5bfb` | 1602 | `fnd/rv-emc` `drafts/readings/B-refs-pulls.txt` | `v2/docs/feasibility/EMCON.md` |
| `rv-emc/readings/B-refs-sockets.txt` | `60a04732a7204aae72dd50c0790037e704d81a20f910edee4600167d3d27343e` | 2312 | `fnd/rv-emc` `drafts/readings/B-refs-sockets.txt` | `v2/docs/feasibility/EMCON.md` |
| `rv-emc/readings/C-lamp-nets.txt` | `dd860919f792dbce068ef86bf2dca524588b6ff2401c423c82198f5dc1c5e549` | 1766 | `fnd/rv-emc` `drafts/readings/C-lamp-nets.txt` | `v2/docs/feasibility/EMCON.md` |
| `rv-emc/readings/C-nets.txt` | `a1fc241f310dd40a98323f3f42e0cf6df51ed98ace7838f0ea3cd4748900741a` | 1634 | `fnd/rv-emc` `drafts/readings/C-nets.txt` | `v2/docs/feasibility/EMCON.md` |
| `rv-emc/readings/D-nets.txt` | `3bc4ebd855e014e8a665d3d9e5b5fe3595a68aeb360e4a53314bb7cfe3e990b7` | 4712 | `fnd/rv-emc` `drafts/readings/D-nets.txt` | `v2/docs/feasibility/EMCON.md` |
| `rv-emc/readings/D-refs.txt` | `da92ccc287b733e2098ce16afc4bf9650715e29daa02259169fa2c1ef5192b92` | 2351 | `fnd/rv-emc` `drafts/readings/D-refs.txt` | `v2/docs/feasibility/EMCON.md` |
| `rv-emc/readings/candidates-vs-main-458b2873.txt` | `6848d919a39d7602a73edcbc0b2c75a2cae095127ba1ca9e0b01f2d00151f5bf` | 2024 | `fnd/rv-emc` `drafts/readings/candidates-vs-main-458b2873.txt` | `v2/docs/feasibility/EMCON.md` |
| `rv-emc/readings/candidates-vs-r6int-1629.txt` | `fd7b8ee080a431bb24e033fe655bc3e62cd9e7c3832834e97928cf4e8b4d8588` | 1758 | `fnd/rv-emc` `drafts/readings/candidates-vs-r6int-1629.txt` | `v2/docs/feasibility/EMCON.md` |
| `rv-emc/readings/claims_check_on_EMCON.judged.txt` | `10d08aea859fc2c6a88ebeb9070e27ef5fde2fcc0078496a3bd6aeaef8105181` | 505 | `fnd/rv-emc` `drafts/readings/claims_check_on_EMCON.judged.txt` | `v2/docs/feasibility/EMCON.md` |
| `rv-emc/readings/claims_check_on_EMCON.verdict.json` | `3e4fe0049c342ed2e059d27a677726ab3cb5e5cf05c8b4895462779cc7f91397` | 794 | `fnd/rv-emc` `drafts/readings/claims_check_on_EMCON.verdict.json` | `v2/docs/feasibility/EMCON.md` |
| `rv-emc/readings/main-01469100-drift.txt` | `7d0875902eb8e72440cf83c871b9fcfaad93b77b2b55cb62190f64ac497aa18a` | 1974 | `fnd/rv-emc` `drafts/readings/main-01469100-drift.txt` | `v2/docs/feasibility/EMCON.md` |
| `rv-emc/readings/main-b69f20db-drift.txt` | `53f19df4b06db4448cde975ade6ccb559be528a4face306bb793fbfbd743e7fa` | 1574 | `fnd/rv-emc` `drafts/readings/main-b69f20db-drift.txt` | `v2/docs/feasibility/EMCON.md` |
| `rv-emc/readings/main-ccf5808e-drift.txt` | `dc5c72304e5a891a2b1db6b85187266a87922fdf0b7a29d01a31da5c6a2b169b` | 3106 | `fnd/rv-emc` `drafts/readings/main-ccf5808e-drift.txt` | `v2/docs/feasibility/EMCON.md` |
| `rv-emc/readings/tx-inhibit-conductor.txt` | `b950ee353e29ff62969480921b749b4c51aa01e49893b936e68468af1134fcf6` | 8800 | `fnd/rv-emc` `drafts/readings/tx-inhibit-conductor.txt` | `v2/docs/feasibility/EMCON.md` |
| `rv-emc/readings/tx_inhibit_r4t-0795c5de_on_main_by_r6d.txt` | `b323525d4e7abece07673643341d633e1363c092705f2fdaebf6fdb4af53bbd7` | 11044 | `fnd/rv-emc` `drafts/readings/tx_inhibit_r4t-0795c5de_on_main_by_r6d.txt` | `v2/docs/feasibility/EMCON.md` |
| `rv-emc/readings/tx_inhibit_r4t-5aece264_on_candidate_set.txt` | `3b95f0fab9795f03cc99193dad8966463bbbf796c4a5ce0aad5e12599ebea743` | 9546 | `fnd/rv-emc` `drafts/readings/tx_inhibit_r4t-5aece264_on_candidate_set.txt` | `v2/docs/feasibility/EMCON.md` |
| `rv-emc/readings/tx_inhibit_r4t-853f3082_on_candidate_set.txt` | `6aeff06e3a721bf7c474242d9cd9289e8f874cd365986c921e1c2b787ff53897` | 8616 | `fnd/rv-emc` `drafts/readings/tx_inhibit_r4t-853f3082_on_candidate_set.txt` | `v2/docs/feasibility/EMCON.md` |
| `rv-emc/readings/tx_inhibit_r4t-e88aa46b_on_candidate_set.txt` | `29b02fdedcf588ea1fb512b3010e848787b37f0bb0598944432fc31f82d73292` | 9588 | `fnd/rv-emc` `drafts/readings/tx_inhibit_r4t-e88aa46b_on_candidate_set.txt` | `v2/docs/feasibility/EMCON.md` |
| `rv-emc/tools/netcompare.py` | `ec843a6b9e7074478359819ef42bb488344025eb122dfffb83191b0412e859d3` | 940 | `fnd/rv-emc` `drafts/tools/netcompare.py` | `v2/docs/feasibility/EMCON.md` |
| `rv-emc/tools/netdump.py` | `eedd50ce04d88dbe354621fb48561785e50f4e9257d9b67015584427be2cb42b` | 938 | `fnd/rv-emc` `drafts/tools/netdump.py` | `v2/docs/feasibility/EMCON.md` |
| `rv-emc/tools/netline.py` | `9097f2d8b9d6857e4dc54f22b02cb77a280409ebc818f617f583eab0e9c7d306` | 479 | `fnd/rv-emc` `drafts/tools/netline.py` | `v2/docs/feasibility/EMCON.md` |
| `rv-emc/tools/refdump.py` | `98c1b6016a00d79ed76ce5bff49aff14fa439d690bddf67db1fd3dbd584d3184` | 901 | `fnd/rv-emc` `drafts/tools/refdump.py` | `v2/docs/feasibility/EMCON.md` |
| `rv-pwr/datasheets/README.md` | `3d119538584511a80717c65082d5488926d570e62f976856a18bbbdbed3770a5` | 4131 | `fnd/rv-pwr` `drafts/datasheets/README.md` | `v2/docs/feasibility/POWER-THERMAL.md` |
| `rv-pwr/pwr-chain-redeclaration.yaml` | `039c72aa6f451dbdb9b68d6ae6946fb3ca02b70cd76f8390569fc39f178f5f45` | 11663 | `fnd/rv-pwr` `drafts/pwr-chain-redeclaration.yaml` | `v2/docs/feasibility/POWER-THERMAL.md` |
| `rv-pwr/pwr-maker-questions.md` | `6d2e5d29b957c80ffe8b973a3cc705a034694f1ef1bb947c8e6574d02850c293` | 2301 | `fnd/rv-pwr` `drafts/pwr-maker-questions.md` | `v2/docs/feasibility/POWER-THERMAL.md` |
| `rv-pwr/pwr-part-temps-rows.yaml` | `cee34b52c6b452593d0f3a7f5ab6b2e4feb4cd1615b9af7e540dd8e90d2cec5e` | 5229 | `fnd/rv-pwr` `drafts/pwr-part-temps-rows.yaml` | `v2/docs/feasibility/POWER-THERMAL.md` |
| `rv-pwr/pwr_budget.json` | `5a616902d2ddab82f25d34ab55d848d06011fb6fbe48c147221d6b442783e462` | 76863 | `fnd/rv-pwr` `drafts/pwr_budget.json` | `v2/docs/feasibility/POWER-THERMAL.md` |
| `rv-pwr/pwr_budget.out` | `58e40cf604804cc9d70c7fbeb1012be4552563fcc8ae7ef6755003c33acb902f` | 47499 | `fnd/rv-pwr` `drafts/pwr_budget.out` | `v2/docs/feasibility/POWER-THERMAL.md` |
| `rv-pwr/pwr_budget.py` | `469d0820b046ef6ff5aceadf422b4166de3d6a02bc50fa5b0c3644704f0f9556` | 67785 | `fnd/rv-pwr` `drafts/pwr_budget.py` | `v2/docs/feasibility/POWER-THERMAL.md` |
| `rv-zer/ZEROIZE-integration.md` | `ea8afca20dcac2f8f0585200ef0383d2b860826141af0cd669c467196e27f5e3` | 14289 | `fnd/rv-zer` `drafts/ZEROIZE-integration.md` | `v2/docs/feasibility/ZEROIZE.md` |
| `rv-zer/datasheets/SOURCES.md` | `e37862cd151f74af7dea3fa29cf920717279a836cd12985e7ab72c5f4118a1ee` | 7306 | `fnd/rv-zer` `drafts/datasheets/SOURCES.md` | `v2/docs/feasibility/ZEROIZE.md` |
| `rv-zer/prices/jlc-ATECC608B-SSHDA-T.json` | `1b75f8c933d888608a11927a2df2335326ff852da6cf0cb35ae1a90c7891848e` | 11976 | `fnd/rv-zer` `drafts/prices/jlc-ATECC608B-SSHDA-T.json` | `v2/docs/feasibility/ZEROIZE.md` |
| `rv-zer/zeroize/zer_budget.py` | `8cdad0569ec3d8140d291da79361ccc9b519592e91decb1bc1547f21624bca9e` | 20269 | `fnd/rv-zer` `drafts/zeroize/zer_budget.py` | `v2/docs/feasibility/ZEROIZE.md` |
| `rv-zer/zeroize/zer_config.py` | `3d4271b2b9aec3e069ebc8d005f802abb07c7e90b186afc50ef5281725f4b795` | 11519 | `fnd/rv-zer` `drafts/zeroize/zer_config.py` | `v2/docs/feasibility/ZEROIZE.md` |
| `ts-net/ts-net-decisions.md` | `78c2dba37c579c4894d12460f2901fec7816b87def759828eb514df7d51fbdff` | 19831 | `fnd/ts-net` `drafts/ts-net-decisions.md` | `v2/ecad/tools/pcb_rules_coverage.yaml` (PWR-001) |
| `w2/w2-power.md` | `960e46bdd58bf857aeb436dc9239ee11b30060fad978ba557f560e1be50a53ec` | 27952 | `fnd/w2` `drafts/w2-power.md` | `v2/docs/feasibility/POWER-THERMAL.md` |
| `w2/w2-runtime.md` | `2b203982023f6fe63a1eecc1103cc3ceb1b6e51f4a858fbe0e79ce365626c9db` | 16780 | `fnd/w2` `drafts/w2-runtime.md` | `v2/docs/feasibility/POWER-THERMAL.md` |
| `w3a/apply_docs.py` | `998b2218f13c3579ee6f051a57d4d023274f582da790da8889dce5d2db6a7550` | 6510 | `fnd/w3a` `drafts/w3a/apply_docs.py` | the w3a commit of `fnd/r8int5` (board A's regeneration and registry notes) |
| `w3a/apply_docs_r8int5.py` | `73c9345aaeb6c9bf0435c517c18c8cab4690caeddedaf337fafc6a794d106bd2` | 8739 | the r8int5 integrator (`apply_docs_r8int5.py`) | the w3a commit of `fnd/r8int5` (board A's regeneration and registry notes) |
| `w3a/apply_registry.py` | `1b8ba02d2763e5abc5bc41265b2bf6e6677966c2f1f38d50e70e40f71ade2633` | 28901 | `fnd/w3a` `drafts/w3a/apply_registry.py` | the w3a commit of `fnd/r8int5` (board A's regeneration and registry notes) |
| `w3a/apply_registry_r8int5.py` | `7868deee7c900aa6fd97d85baa9e984a366d23f4724085f751e1d32cd4495e18` | 31117 | the r8int5 integrator (`apply_registry_r8int5.py`) | the w3a commit of `fnd/r8int5` (board A's regeneration and registry notes) |
| `w3a/coverage_and_sources_w3a.py` | `af4b273ac07bcd10938f3b271ec9aa8aeb4b95f148b6f87eb78005ac848cd018` | 7453 | the r8int5 integrator (`coverage_and_sources_w3a.py`) | the w3a commit of `fnd/r8int5` (board A's regeneration and registry notes) |
| `w3a/gen_sch_a-linemap.json` | `ac0e59552ab7c30cca1d6bcc627ef5432580fd6fb67bd262f9edb839771de143` | 16425 | `fnd/w3a` `drafts/w3a/gen_sch_a-linemap.json` | the w3a commit of `fnd/r8int5` (board A's regeneration and registry notes) |
| `w3a/parity/netcmp.py` | `234317d8d308042752f91f45eb3362ca49222d65282d1b6bc6a74e266b2f3ae7` | 3633 | `fnd/w3a` `drafts/w3a/parity/netcmp.py` | the w3a commit of `fnd/r8int5` (board A's regeneration and registry notes) |
| `w3a/parity/parity-candidate-vs-main.json` | `c2880474d72d0e9cd51a28391d22589738553976885c3d53dfbbed182be9e9e4` | 8181 | `fnd/w3a` `drafts/w3a/parity/parity-candidate-vs-main.json` | the w3a commit of `fnd/r8int5` (board A's regeneration and registry notes) |
| `w3a/parity/parity-main-regeneration-vs-committed.json` | `aba314a41e32521a6e49c3a2a6a3bd387b5d147f2e063b58d6a30fe52c595b7c` | 254 | `fnd/w3a` `drafts/w3a/parity/parity-main-regeneration-vs-committed.json` | the w3a commit of `fnd/r8int5` (board A's regeneration and registry notes) |
| `w3a/parity/pass2-rerun/compare.txt` | `384536fe9feb9adb1892c27db9c9974d91bdcf5cc64515b91e3bb7fc505b38fd` | 686 | `fnd/w3a` `drafts/w3a/parity/pass2-rerun/compare.txt` | the w3a commit of `fnd/r8int5` (board A's regeneration and registry notes) |
| `w3a/parity/pass2-rerun/erc_gate.log` | `08866e2d87680805eacf5885419620569176669a556394f5743cc579c44e6610` | 583 | `fnd/w3a` `drafts/w3a/parity/pass2-rerun/erc_gate.log` | the w3a commit of `fnd/r8int5` (board A's regeneration and registry notes) |
| `w3a/parity/pass2-rerun/erc_gate.verdict.json` | `7cb408cc2c1ffc4cf4d7a054d02e66e47cfe67b6ce942277203c47440292684a` | 1749 | `fnd/w3a` `drafts/w3a/parity/pass2-rerun/erc_gate.verdict.json` | the w3a commit of `fnd/r8int5` (board A's regeneration and registry notes) |
| `w3a/parity/pass2-rerun/gen_sch.log` | `5b418a433e122b0ed9a00397cf8767fea4a63556a03c5334c7417776782dc6e2` | 474 | `fnd/w3a` `drafts/w3a/parity/pass2-rerun/gen_sch.log` | the w3a commit of `fnd/r8int5` (board A's regeneration and registry notes) |
| `w3a/parity/pass2-rerun/pcb-a-power.net.prov.json` | `b22848e7d502b694185d5e8335d855159368a68de6d0666c15e79ea978cd61b4` | 8641 | `fnd/w3a` `drafts/w3a/parity/pass2-rerun/pcb-a-power.net.prov.json` | the w3a commit of `fnd/r8int5` (board A's regeneration and registry notes) |
| `w3a/parity/pass2-rerun/power_path.log` | `2a5c10c3ad74bee52be4060ceec2ea2d5bef6d6a7c901d2bd85d9dc73dcc904c` | 1650 | `fnd/w3a` `drafts/w3a/parity/pass2-rerun/power_path.log` | the w3a commit of `fnd/r8int5` (board A's regeneration and registry notes) |
| `w3a/parity/regen.sh` | `01d6ad798587a8bf2bed2ce5acc0459e1e66706351305e0d472dd99067f04e1c` | 2208 | `fnd/w3a` `drafts/w3a/parity/regen.sh` | the w3a commit of `fnd/r8int5` (board A's regeneration and registry notes) |
| `w3a/readings/after/derate.txt` | `65e0cd7d8aed46a387ea816c872fe3e7a3af78976d84da120b94db43d10d06af` | 587 | `fnd/w3a` `drafts/w3a/readings/after/derate.txt` | the w3a commit of `fnd/r8int5` (board A's regeneration and registry notes) |
| `w3a/readings/after/derate.verdict.json` | `71227021ee715a94723cdf62cd0af8cea7f7addce8e1da8c5e867cd6fbc59543` | 1276 | `fnd/w3a` `drafts/w3a/readings/after/derate.verdict.json` | the w3a commit of `fnd/r8int5` (board A's regeneration and registry notes) |
| `w3a/readings/after/erc_gate.verdict.json` | `eaf2e7924fad9afca2f7de138c57107b99aaad01d5f880399566f890c218cec3` | 1749 | `fnd/w3a` `drafts/w3a/readings/after/erc_gate.verdict.json` | the w3a commit of `fnd/r8int5` (board A's regeneration and registry notes) |
| `w3a/readings/after/intent_rails.verdict.json` | `d5a65203a3750f76e7acdc139f409256bbbb05b17b28eccf1872937e4e0b2148` | 11044 | `fnd/w3a` `drafts/w3a/readings/after/intent_rails.verdict.json` | the w3a commit of `fnd/r8int5` (board A's regeneration and registry notes) |
| `w3a/readings/after/port_protect.verdict.json` | `245b46e3a730e7804ac92b831e16ba62bdcc0ed5655db6086217747961652900` | 1717 | `fnd/w3a` `drafts/w3a/readings/after/port_protect.verdict.json` | the w3a commit of `fnd/r8int5` (board A's regeneration and registry notes) |
| `w3a/readings/after/port_protect_a.verdict.json` | `c2536d1dac79380e7965cb81b1f6d3b58ed7408462eb97c7a95ee783828b7e73` | 1796 | `fnd/w3a` `drafts/w3a/readings/after/port_protect_a.verdict.json` | the w3a commit of `fnd/r8int5` (board A's regeneration and registry notes) |
| `w3a/readings/after/power_path.log` | `c45bec39316ac79a33328d4624e7621a2cefd808e115231f655310d483f56f02` | 1648 | `fnd/w3a` `drafts/w3a/readings/after/power_path.log` | the w3a commit of `fnd/r8int5` (board A's regeneration and registry notes) |
| `w3a/readings/after/power_sequence.verdict.json` | `c812bd70f7e7fd7054f8d2ff33b87969491a3b1a709f6e43e671986de25b3905` | 1736 | `fnd/w3a` `drafts/w3a/readings/after/power_sequence.verdict.json` | the w3a commit of `fnd/r8int5` (board A's regeneration and registry notes) |
| `w3a/readings/after/pp.txt` | `bfaa9a9feffa71c069175534741da915cf832088f2c0eba96e10f1f8830fe5ba` | 1594 | `fnd/w3a` `drafts/w3a/readings/after/pp.txt` | the w3a commit of `fnd/r8int5` (board A's regeneration and registry notes) |
| `w3a/readings/after/pseq.txt` | `3952459a8f86d6069d5cecafd11a4242213249e6a3d8e226f681d6c90eadef34` | 3448 | `fnd/w3a` `drafts/w3a/readings/after/pseq.txt` | the w3a commit of `fnd/r8int5` (board A's regeneration and registry notes) |
| `w3a/readings/after/pwr001.txt` | `e7f9c137b1e1817c11f2f00bb187f053f643b7fc065ed8a7d31f3ecd754cdc7f` | 18443 | `fnd/w3a` `drafts/w3a/readings/after/pwr001.txt` | the w3a commit of `fnd/r8int5` (board A's regeneration and registry notes) |
| `w3a/readings/before/derate.txt` | `425d1418902e0f92c727145fef368e75f75b98eb8c50046fc92e4c23dc5700ed` | 587 | `fnd/w3a` `drafts/w3a/readings/before/derate.txt` | the w3a commit of `fnd/r8int5` (board A's regeneration and registry notes) |
| `w3a/readings/before/derate.verdict.json` | `b4549dce54da191976ac84d7ecbfa4ca4996107f755757a90df639a22e7ba224` | 1289 | `fnd/w3a` `drafts/w3a/readings/before/derate.verdict.json` | the w3a commit of `fnd/r8int5` (board A's regeneration and registry notes) |
| `w3a/readings/before/erc_gate.verdict.json` | `67816dfe486acdbccf170e8325f71f50dca9a4b5c7e7645961de4eb2f995e0fc` | 1749 | `fnd/w3a` `drafts/w3a/readings/before/erc_gate.verdict.json` | the w3a commit of `fnd/r8int5` (board A's regeneration and registry notes) |
| `w3a/readings/before/intent_rails.verdict.json` | `405ae0f5a0fc99b61b2f7dde2b1ca276a70ddc73c882f74b97f763e83d4fcb62` | 11859 | `fnd/w3a` `drafts/w3a/readings/before/intent_rails.verdict.json` | the w3a commit of `fnd/r8int5` (board A's regeneration and registry notes) |
| `w3a/readings/before/port_protect.verdict.json` | `560cb60a1346c8e5b1483c7c927dcea43b03ee453a775084967897934a57e9f7` | 1711 | `fnd/w3a` `drafts/w3a/readings/before/port_protect.verdict.json` | the w3a commit of `fnd/r8int5` (board A's regeneration and registry notes) |
| `w3a/readings/before/port_protect_a.verdict.json` | `6f2ab741b709822d8293e4248f2694ff18266b64057e2527d930f7963b0fa616` | 1790 | `fnd/w3a` `drafts/w3a/readings/before/port_protect_a.verdict.json` | the w3a commit of `fnd/r8int5` (board A's regeneration and registry notes) |
| `w3a/readings/before/power_sequence.verdict.json` | `a890b93bd0710b5ce813bee53e24230c711b47964e90fc0ab20a8b7fcf1df759` | 1730 | `fnd/w3a` `drafts/w3a/readings/before/power_sequence.verdict.json` | the w3a commit of `fnd/r8int5` (board A's regeneration and registry notes) |
| `w3a/readings/before/pp.txt` | `bfaa9a9feffa71c069175534741da915cf832088f2c0eba96e10f1f8830fe5ba` | 1594 | `fnd/w3a` `drafts/w3a/readings/before/pp.txt` | the w3a commit of `fnd/r8int5` (board A's regeneration and registry notes) |
| `w3a/readings/before/pseq.txt` | `cbb983fb9637c70a020762a7abad4e6a20763f4d4f4271646846e79652b6c408` | 3150 | `fnd/w3a` `drafts/w3a/readings/before/pseq.txt` | the w3a commit of `fnd/r8int5` (board A's regeneration and registry notes) |
| `w3a/readings/before/pwr001.txt` | `e44ae5f420997c597a468473f040ac9bca2dc94ee87e33aa85b2593e8b158c49` | 18795 | `fnd/w3a` `drafts/w3a/readings/before/pwr001.txt` | the w3a commit of `fnd/r8int5` (board A's regeneration and registry notes) |
| `w3a/readings/rf002-after.txt` | `e646da888fd259e72c886797b0b528504875f69f7dedf58b46792f2c5707a2b7` | 18638 | `fnd/w3a` `drafts/w3a/readings/rf002-after.txt` | the w3a commit of `fnd/r8int5` (board A's regeneration and registry notes) |
| `w3a/readings/rf002-before.txt` | `7e1270ebf6bfd1b0ee97bb01e750c5006957e9d6551a842d5d9ebb468e227fa3` | 18620 | `fnd/w3a` `drafts/w3a/readings/rf002-before.txt` | the w3a commit of `fnd/r8int5` (board A's regeneration and registry notes) |
| `w3a/readings/tests-pass2.txt` | `785bb1bb5da8a7303bc08fb43c1d9188446fb4e8730bda53f3dd5ff47bd5a93e` | 50497 | `fnd/w3a` `drafts/w3a/readings/tests-pass2.txt` | the w3a commit of `fnd/r8int5` (board A's regeneration and registry notes) |
| `w3a/readings/tests-targeted.txt` | `f6de29d01f56b2cc27a28fb65081d67e2bb2fcc04b9da955ea9efd27ef0b8935` | 33688 | `fnd/w3a` `drafts/w3a/readings/tests-targeted.txt` | the w3a commit of `fnd/r8int5` (board A's regeneration and registry notes) |
| `w3a/sources-w3a.yaml` | `a8c5151c7639db352b58052379b61483696222113e7529da88201ce6b2b95d20` | 4576 | `fnd/w3a` `drafts/w3a/sources-w3a.yaml` | the w3a commit of `fnd/r8int5` (board A's regeneration and registry notes) |
| `w3a/test_rails_census-replay-state.patch` | `8fca30488fa016ba7cdaa20686e769ce75a8ae60fe53a2489977ee18380761c9` | 938 | `fnd/w3a` `drafts/w3a/test_rails_census-replay-state.patch` | the w3a commit of `fnd/r8int5` (board A's regeneration and registry notes) |
| `w3b/apply_registry.py` | `3a140fdbd7e1db1029a8c2798ef7e4d43e9adcb4ca008a953748047ae3b0d384` | 15860 | `fnd/w3b` `drafts/w3b/apply_registry.py` | the w3b commit of `fnd/r8int5` (gen_sch_b.py, the registry notes, DECOUPLING.md section 10) |
| `w3b/apply_registry_r8int5.py` | `3a9f70f6fffdd46f83683a993db12aea8f8e6378a88677a64f0e66b265d5aefe` | 16831 | the r8int5 integrator (`apply_registry_r8int5.py`) | the w3b commit of `fnd/r8int5` (gen_sch_b.py, the registry notes, DECOUPLING.md section 10) |
| `w3b/evidence/box/build_sch-base.log` | `a99e71c2a2843de33e44b323304311cd3c1f1e1b2180bd641e3e99dda819e54e` | 586 | `fnd/w3b` `drafts/w3b/evidence/box/build_sch-base.log` | the w3b commit of `fnd/r8int5` (gen_sch_b.py, the registry notes, DECOUPLING.md section 10) |
| `w3b/evidence/box/build_sch-cand.log` | `1b5c0da5519a67d761a98c84dec3fd4194c44d39080f90f313aa579c9599a42f` | 586 | `fnd/w3b` `drafts/w3b/evidence/box/build_sch-cand.log` | the w3b commit of `fnd/r8int5` (gen_sch_b.py, the registry notes, DECOUPLING.md section 10) |
| `w3b/evidence/box/compare-intermediate-gnd-omitted.log` | `6331dc97779efd1ca6c10a34033536332333cd5190611d4d48ebee39dd61ef9d` | 1939 | `fnd/w3b` `drafts/w3b/evidence/box/compare-intermediate-gnd-omitted.log` | the w3b commit of `fnd/r8int5` (gen_sch_b.py, the registry notes, DECOUPLING.md section 10) |
| `w3b/evidence/box/compare.log` | `fc2d9217f675e6679f4c12d63c8ce55b6d4bb015a41ace0b21f149eb308766b5` | 1833 | `fnd/w3b` `drafts/w3b/evidence/box/compare.log` | the w3b commit of `fnd/r8int5` (gen_sch_b.py, the registry notes, DECOUPLING.md section 10) |
| `w3b/evidence/box/compare/base_vs_committed_bom.json` | `49fa6a4ae200094d9e1f2253d63c0b7ae64d1af3d79bbc01f19c5b045b9010a3` | 68 | `fnd/w3b` `drafts/w3b/evidence/box/compare/base_vs_committed_bom.json` | the w3b commit of `fnd/r8int5` (gen_sch_b.py, the registry notes, DECOUPLING.md section 10) |
| `w3b/evidence/box/compare/base_vs_committed_erc.json` | `bee8b3db674241f3fae67e0377a4a774706ea66debe2490f3ac77e788542ef84` | 485 | `fnd/w3b` `drafts/w3b/evidence/box/compare/base_vs_committed_erc.json` | the w3b commit of `fnd/r8int5` (gen_sch_b.py, the registry notes, DECOUPLING.md section 10) |
| `w3b/evidence/box/compare/base_vs_committed_intent.json` | `607f2e1b7adb75dc66267217a7334114126f37ea6ca8cab0548736b90c1ba3d4` | 76 | `fnd/w3b` `drafts/w3b/evidence/box/compare/base_vs_committed_intent.json` | the w3b commit of `fnd/r8int5` (gen_sch_b.py, the registry notes, DECOUPLING.md section 10) |
| `w3b/evidence/box/compare/base_vs_committed_netlist.json` | `ec85095b86bf29f7ea4cd8a61d85fc775dd8f06461b7dd20c430982c1cd41aa6` | 719 | `fnd/w3b` `drafts/w3b/evidence/box/compare/base_vs_committed_netlist.json` | the w3b commit of `fnd/r8int5` (gen_sch_b.py, the registry notes, DECOUPLING.md section 10) |
| `w3b/evidence/box/compare/base_vs_committed_provenance.json` | `beaf5c58de8d3847e983c2730098b050055c47053475cde02de9a08d3210df35` | 80 | `fnd/w3b` `drafts/w3b/evidence/box/compare/base_vs_committed_provenance.json` | the w3b commit of `fnd/r8int5` (gen_sch_b.py, the registry notes, DECOUPLING.md section 10) |
| `w3b/evidence/box/compare/base_vs_committed_schematic.json` | `ae0669e008778caeef8abacf82b910c30b6718d65ac96ed67c81e066696088a0` | 351 | `fnd/w3b` `drafts/w3b/evidence/box/compare/base_vs_committed_schematic.json` | the w3b commit of `fnd/r8int5` (gen_sch_b.py, the registry notes, DECOUPLING.md section 10) |
| `w3b/evidence/box/compare/cand_vs_base_bom.json` | `164eac0281d4c760e5d724fce2005481e43074b16293e618580ad746de19d0ae` | 1854 | `fnd/w3b` `drafts/w3b/evidence/box/compare/cand_vs_base_bom.json` | the w3b commit of `fnd/r8int5` (gen_sch_b.py, the registry notes, DECOUPLING.md section 10) |
| `w3b/evidence/box/compare/cand_vs_base_erc.json` | `ca027d4e2f7546801bd71b70f96367c92c335d06483dd4eb5b01fdc2cf82d11a` | 2934 | `fnd/w3b` `drafts/w3b/evidence/box/compare/cand_vs_base_erc.json` | the w3b commit of `fnd/r8int5` (gen_sch_b.py, the registry notes, DECOUPLING.md section 10) |
| `w3b/evidence/box/compare/cand_vs_base_intent.json` | `3831d89bf7be4ac251a41557a004af5fc975d91961875df923bfaa1d41b2ab12` | 102 | `fnd/w3b` `drafts/w3b/evidence/box/compare/cand_vs_base_intent.json` | the w3b commit of `fnd/r8int5` (gen_sch_b.py, the registry notes, DECOUPLING.md section 10) |
| `w3b/evidence/box/compare/cand_vs_base_netlist.json` | `be9dd79a01e5890e960744e9fd908ed7371c273e7acc0c59c2d76eaac4804d39` | 5606 | `fnd/w3b` `drafts/w3b/evidence/box/compare/cand_vs_base_netlist.json` | the w3b commit of `fnd/r8int5` (gen_sch_b.py, the registry notes, DECOUPLING.md section 10) |
| `w3b/evidence/box/compare/cand_vs_base_schematic.json` | `efd099859690682d41740c8333beffda2113a4988bd76badf22ef65e557e935d` | 9547 | `fnd/w3b` `drafts/w3b/evidence/box/compare/cand_vs_base_schematic.json` | the w3b commit of `fnd/r8int5` (gen_sch_b.py, the registry notes, DECOUPLING.md section 10) |
| `w3b/evidence/box/compare/indep_committed_vs_cand.txt` | `793b3219924565d438384f04f384172d372a4efa8e7b87354184945d223dc4c2` | 75 | `fnd/w3b` `drafts/w3b/evidence/box/compare/indep_committed_vs_cand.txt` | the w3b commit of `fnd/r8int5` (gen_sch_b.py, the registry notes, DECOUPLING.md section 10) |
| `w3b/evidence/box/compare/indep_committed_vs_mainregen.txt` | `8e054141b90dd07a0cfb0136918a0cfbd334d4c5fd2b4a00c3e7ede54316942d` | 188 | `fnd/w3b` `drafts/w3b/evidence/box/compare/indep_committed_vs_mainregen.txt` | the w3b commit of `fnd/r8int5` (gen_sch_b.py, the registry notes, DECOUPLING.md section 10) |
| `w3b/evidence/box/compare/indep_dropped.txt` | `19588d28d92c85f0b5cc93fc2cd5890bbdb8ab7879bfbb9b6a99c78d96b87283` | 137 | `fnd/w3b` `drafts/w3b/evidence/box/compare/indep_dropped.txt` | the w3b commit of `fnd/r8int5` (gen_sch_b.py, the registry notes, DECOUPLING.md section 10) |
| `w3b/evidence/box/compare/indep_mainregen_vs_cand.txt` | `793b3219924565d438384f04f384172d372a4efa8e7b87354184945d223dc4c2` | 75 | `fnd/w3b` `drafts/w3b/evidence/box/compare/indep_mainregen_vs_cand.txt` | the w3b commit of `fnd/r8int5` (gen_sch_b.py, the registry notes, DECOUPLING.md section 10) |
| `w3b/evidence/box/compare/rename_check.txt` | `398357dc291da81dd8f542a64d439cbc07296f13face908e799ea287a5123d93` | 243 | `fnd/w3b` `drafts/w3b/evidence/box/compare/rename_check.txt` | the w3b commit of `fnd/r8int5` (gen_sch_b.py, the registry notes, DECOUPLING.md section 10) |
| `w3b/evidence/box/gates.log` | `c3188d0d7502dba25f2e0ca693622ad7aca793a93755b442fa74e5f779c4042a` | 870 | `fnd/w3b` `drafts/w3b/evidence/box/gates.log` | the w3b commit of `fnd/r8int5` (gen_sch_b.py, the registry notes, DECOUPLING.md section 10) |
| `w3b/evidence/box/gen_sch-base.log` | `d82d5dcc924772b1271ee925669a6e55d17843c39fec85eddb5f326c53f55caa` | 999 | `fnd/w3b` `drafts/w3b/evidence/box/gen_sch-base.log` | the w3b commit of `fnd/r8int5` (gen_sch_b.py, the registry notes, DECOUPLING.md section 10) |
| `w3b/evidence/box/gen_sch-cand.log` | `c74dd287ab039725d6954f049aac7f2eb78a9e9ea47e2b8516711b6fae38fb4c` | 999 | `fnd/w3b` `drafts/w3b/evidence/box/gen_sch-cand.log` | the w3b commit of `fnd/r8int5` (gen_sch_b.py, the registry notes, DECOUPLING.md section 10) |
| `w3b/evidence/box/incoming.sha256` | `e6b28e71923ae0287a915def5c0afe64b9117fb0b87fbbf7a30370863b2829a8` | 324 | `fnd/w3b` `drafts/w3b/evidence/box/incoming.sha256` | the w3b commit of `fnd/r8int5` (gen_sch_b.py, the registry notes, DECOUPLING.md section 10) |
| `w3b/evidence/box/prov-after-base.txt` | `bf16f7ffdff8b652e0b0bb93093cc4290847ca4916be2a37b95b467b5a427a22` | 95 | `fnd/w3b` `drafts/w3b/evidence/box/prov-after-base.txt` | the w3b commit of `fnd/r8int5` (gen_sch_b.py, the registry notes, DECOUPLING.md section 10) |
| `w3b/evidence/box/prov-after-cand.txt` | `49dc87c9fa01343f453df41e2b6a671262d73744a1b484077f8b23a442dc66b6` | 95 | `fnd/w3b` `drafts/w3b/evidence/box/prov-after-cand.txt` | the w3b commit of `fnd/r8int5` (gen_sch_b.py, the registry notes, DECOUPLING.md section 10) |
| `w3b/evidence/box/regen.log` | `bf4e781ecbf0e32e9a982261dc617916d10f7fe2f2170b70512b68eb71aa7ca7` | 1020 | `fnd/w3b` `drafts/w3b/evidence/box/regen.log` | the w3b commit of `fnd/r8int5` (gen_sch_b.py, the registry notes, DECOUPLING.md section 10) |
| `w3b/evidence/box/setup.log` | `e74e553e22da72fe9b2bf105f0e913f04a5af16e025fa5cc1195f3a196cd10ac` | 667 | `fnd/w3b` `drafts/w3b/evidence/box/setup.log` | the w3b commit of `fnd/r8int5` (gen_sch_b.py, the registry notes, DECOUPLING.md section 10) |
| `w3b/evidence/decoupling-classes-w3b.txt` | `e58028b64e513242effa939e256b72ca53c811211aa3cae64eb4f3c3c73ff095` | 2071 | `fnd/w3b` `drafts/w3b/evidence/decoupling-classes-w3b.txt` | the w3b commit of `fnd/r8int5` (gen_sch_b.py, the registry notes, DECOUPLING.md section 10) |
| `w3b/evidence/gates-after/check_contracts.log` | `757343a55caf14774bf371cfc0e0cbf2474ac45b4461f9560fa5b7819b89b2d3` | 24221 | `fnd/w3b` `drafts/w3b/evidence/gates-after/check_contracts.log` | the w3b commit of `fnd/r8int5` (gen_sch_b.py, the registry notes, DECOUPLING.md section 10) |
| `w3b/evidence/gates-after/check_contracts.verdict.json` | `c5003bd13b094d381dbe6faf4a7ccf2546e35bbc011d4692d1d198f4eceb95ec` | 2947 | `fnd/w3b` `drafts/w3b/evidence/gates-after/check_contracts.verdict.json` | the w3b commit of `fnd/r8int5` (gen_sch_b.py, the registry notes, DECOUPLING.md section 10) |
| `w3b/evidence/gates-after/check_contracts_a.verdict.json` | `e435586dff2eee0d99b295dba177a2cc143320b9872ed1046318a9b5053a8178` | 2699 | `fnd/w3b` `drafts/w3b/evidence/gates-after/check_contracts_a.verdict.json` | the w3b commit of `fnd/r8int5` (gen_sch_b.py, the registry notes, DECOUPLING.md section 10) |
| `w3b/evidence/gates-after/check_contracts_b.verdict.json` | `39d35a7a31b4264e595fff81f41f383aa94d6f1c7bd77d2e240268dba48a17f3` | 2444 | `fnd/w3b` `drafts/w3b/evidence/gates-after/check_contracts_b.verdict.json` | the w3b commit of `fnd/r8int5` (gen_sch_b.py, the registry notes, DECOUPLING.md section 10) |
| `w3b/evidence/gates-after/check_contracts_c.verdict.json` | `e4aa40b65d59a1557d8fc49c5f8e0f614bb6997c39f04e580a3f8c5644cef315` | 2442 | `fnd/w3b` `drafts/w3b/evidence/gates-after/check_contracts_c.verdict.json` | the w3b commit of `fnd/r8int5` (gen_sch_b.py, the registry notes, DECOUPLING.md section 10) |
| `w3b/evidence/gates-after/check_contracts_d.verdict.json` | `c461c416f46676782574750d135f15370748e7a8298105003f5344bdcc7a5345` | 2444 | `fnd/w3b` `drafts/w3b/evidence/gates-after/check_contracts_d.verdict.json` | the w3b commit of `fnd/r8int5` (gen_sch_b.py, the registry notes, DECOUPLING.md section 10) |
| `w3b/evidence/gates-after/check_contracts_e.verdict.json` | `b95eddf1be701124d0ab0398a1507c899fa47ffa27716359ed09fc4b8a1b629d` | 2171 | `fnd/w3b` `drafts/w3b/evidence/gates-after/check_contracts_e.verdict.json` | the w3b commit of `fnd/r8int5` (gen_sch_b.py, the registry notes, DECOUPLING.md section 10) |
| `w3b/evidence/gates-after/check_contracts_p.verdict.json` | `07e26f204e6c0e130ae03fa11b6f7ea3217d7978e6b9b246fe4ae75e2f344017` | 1912 | `fnd/w3b` `drafts/w3b/evidence/gates-after/check_contracts_p.verdict.json` | the w3b commit of `fnd/r8int5` (gen_sch_b.py, the registry notes, DECOUPLING.md section 10) |
| `w3b/evidence/gates-after/clock_check.log` | `0f52220d2d6615664516b6b28aec64c63f14908fdcb00e265e5eb342c3194e8f` | 1386 | `fnd/w3b` `drafts/w3b/evidence/gates-after/clock_check.log` | the w3b commit of `fnd/r8int5` (gen_sch_b.py, the registry notes, DECOUPLING.md section 10) |
| `w3b/evidence/gates-after/clock_check.verdict.json` | `3cfe33a1988e13f17c646782f5811e89bbfa631e7119db6de0e3aedcf6da5d4d` | 1264 | `fnd/w3b` `drafts/w3b/evidence/gates-after/clock_check.verdict.json` | the w3b commit of `fnd/r8int5` (gen_sch_b.py, the registry notes, DECOUPLING.md section 10) |
| `w3b/evidence/gates-after/derate.log` | `7272dd3e46d32606f64f738634beff8149c2c12313d780c62a2ce15d3857f76c` | 595 | `fnd/w3b` `drafts/w3b/evidence/gates-after/derate.log` | the w3b commit of `fnd/r8int5` (gen_sch_b.py, the registry notes, DECOUPLING.md section 10) |
| `w3b/evidence/gates-after/derate.verdict.json` | `22b910e83dc9528ee2e6616e61144ed203a0acfc5ddd22474836cda980013e6c` | 1299 | `fnd/w3b` `drafts/w3b/evidence/gates-after/derate.verdict.json` | the w3b commit of `fnd/r8int5` (gen_sch_b.py, the registry notes, DECOUPLING.md section 10) |
| `w3b/evidence/gates-after/edge_length.log` | `600705e3cd0e98ea58c61084b93ed58f75dc2891e494ea98d20b5bccda0a8ecc` | 12581 | `fnd/w3b` `drafts/w3b/evidence/gates-after/edge_length.log` | the w3b commit of `fnd/r8int5` (gen_sch_b.py, the registry notes, DECOUPLING.md section 10) |
| `w3b/evidence/gates-after/edge_length.verdict.json` | `2acc2c693899506d577d5a49ed64fca6af09e157f4162930ebc76d4ed1bd7296` | 27402 | `fnd/w3b` `drafts/w3b/evidence/gates-after/edge_length.verdict.json` | the w3b commit of `fnd/r8int5` (gen_sch_b.py, the registry notes, DECOUPLING.md section 10) |
| `w3b/evidence/gates-after/energy_chain.log` | `9ec7be1be121756e26bf2c06366ce9c0b2fdce213c26b63f4c1e9d395080bccd` | 2579 | `fnd/w3b` `drafts/w3b/evidence/gates-after/energy_chain.log` | the w3b commit of `fnd/r8int5` (gen_sch_b.py, the registry notes, DECOUPLING.md section 10) |
| `w3b/evidence/gates-after/energy_chain.verdict.json` | `ff75c5e379954ac2b129cca4f9b8816ec723315ae8848e8a0e4d493e5c9afc52` | 2485 | `fnd/w3b` `drafts/w3b/evidence/gates-after/energy_chain.verdict.json` | the w3b commit of `fnd/r8int5` (gen_sch_b.py, the registry notes, DECOUPLING.md section 10) |
| `w3b/evidence/gates-after/energy_chain_a.verdict.json` | `c372dc3d6c81b04d08ccdd11df2c427a67e01f0b0883b44f054ef351bcec287a` | 1756 | `fnd/w3b` `drafts/w3b/evidence/gates-after/energy_chain_a.verdict.json` | the w3b commit of `fnd/r8int5` (gen_sch_b.py, the registry notes, DECOUPLING.md section 10) |
| `w3b/evidence/gates-after/energy_chain_b.verdict.json` | `110ccb3510cbf618ebda6f580f4a5a3a2cb6c51c1747f0b6394f0f9cce28d6a5` | 1618 | `fnd/w3b` `drafts/w3b/evidence/gates-after/energy_chain_b.verdict.json` | the w3b commit of `fnd/r8int5` (gen_sch_b.py, the registry notes, DECOUPLING.md section 10) |
| `w3b/evidence/gates-after/energy_chain_e.verdict.json` | `9dccb5665c1e46503ec4f36175607177eefd7ab3ea2b4e35e5d22c22e6dcd8c6` | 1756 | `fnd/w3b` `drafts/w3b/evidence/gates-after/energy_chain_e.verdict.json` | the w3b commit of `fnd/r8int5` (gen_sch_b.py, the registry notes, DECOUPLING.md section 10) |
| `w3b/evidence/gates-after/energy_chain_e5.verdict.json` | `09dc936163e3c99172f1f68d495f3d90aa8a69dac24882dc639d7391c7bba342` | 1564 | `fnd/w3b` `drafts/w3b/evidence/gates-after/energy_chain_e5.verdict.json` | the w3b commit of `fnd/r8int5` (gen_sch_b.py, the registry notes, DECOUPLING.md section 10) |
| `w3b/evidence/gates-after/energy_chain_p.verdict.json` | `cc317a120e47c5154c07f27dce3e0d092dd5d38838a5f2eb223abe59e3f9a238` | 1612 | `fnd/w3b` `drafts/w3b/evidence/gates-after/energy_chain_p.verdict.json` | the w3b commit of `fnd/r8int5` (gen_sch_b.py, the registry notes, DECOUPLING.md section 10) |
| `w3b/evidence/gates-after/ground_system.log` | `5eeea039935262ffa6b999d5039b902d25598faf4800c0f04fa88bf1276f521a` | 381 | `fnd/w3b` `drafts/w3b/evidence/gates-after/ground_system.log` | the w3b commit of `fnd/r8int5` (gen_sch_b.py, the registry notes, DECOUPLING.md section 10) |
| `w3b/evidence/gates-after/ground_system.verdict.json` | `1e8d806275880c5181291ddb06b062a6e1e3b8d5760bb22104b2b2fdb7266e78` | 1270 | `fnd/w3b` `drafts/w3b/evidence/gates-after/ground_system.verdict.json` | the w3b commit of `fnd/r8int5` (gen_sch_b.py, the registry notes, DECOUPLING.md section 10) |
| `w3b/evidence/gates-after/inhibit_chain_a.verdict.json` | `d5ac77bdeac49a25e09138d33d0a1e55642c0e81c04e684048d75fefada9488a` | 4276 | `fnd/w3b` `drafts/w3b/evidence/gates-after/inhibit_chain_a.verdict.json` | the w3b commit of `fnd/r8int5` (gen_sch_b.py, the registry notes, DECOUPLING.md section 10) |
| `w3b/evidence/gates-after/inhibit_chain_b.verdict.json` | `13ae203fad9b3b692586e7e5c566cf5d890fc6df30a59520a1db6c9b6ca49f6e` | 5388 | `fnd/w3b` `drafts/w3b/evidence/gates-after/inhibit_chain_b.verdict.json` | the w3b commit of `fnd/r8int5` (gen_sch_b.py, the registry notes, DECOUPLING.md section 10) |
| `w3b/evidence/gates-after/inhibit_chain_c.verdict.json` | `b6d4505b2aaef1a86af2ab21ae18e7a2a8c3772c9f99cb8067b24297b2c7e3cd` | 3808 | `fnd/w3b` `drafts/w3b/evidence/gates-after/inhibit_chain_c.verdict.json` | the w3b commit of `fnd/r8int5` (gen_sch_b.py, the registry notes, DECOUPLING.md section 10) |
| `w3b/evidence/gates-after/inhibit_chain_d.verdict.json` | `07b9efebd5b75e453be81f37f4973c11c217d50252f13f940345598ba63eb772` | 3637 | `fnd/w3b` `drafts/w3b/evidence/gates-after/inhibit_chain_d.verdict.json` | the w3b commit of `fnd/r8int5` (gen_sch_b.py, the registry notes, DECOUPLING.md section 10) |
| `w3b/evidence/gates-after/inhibit_chain_e.verdict.json` | `7408020715eefbedaf8b01ac0f28a6b53a975b20debd03add3e730041fbb1237` | 2907 | `fnd/w3b` `drafts/w3b/evidence/gates-after/inhibit_chain_e.verdict.json` | the w3b commit of `fnd/r8int5` (gen_sch_b.py, the registry notes, DECOUPLING.md section 10) |
| `w3b/evidence/gates-after/inhibit_chain_p.verdict.json` | `b0c2adf5aa1af2dcab7eb41c1f8b07ee96975a2aa2afbb3c115bdad509f6c6de` | 2650 | `fnd/w3b` `drafts/w3b/evidence/gates-after/inhibit_chain_p.verdict.json` | the w3b commit of `fnd/r8int5` (gen_sch_b.py, the registry notes, DECOUPLING.md section 10) |
| `w3b/evidence/gates-after/intent_rails.log` | `0e95f98d978b40574e0e89f9f92b9465fa1fea4124ca2fa7a7175043343ef4ac` | 16693 | `fnd/w3b` `drafts/w3b/evidence/gates-after/intent_rails.log` | the w3b commit of `fnd/r8int5` (gen_sch_b.py, the registry notes, DECOUPLING.md section 10) |
| `w3b/evidence/gates-after/intent_rails.verdict.json` | `28c4febfecfe8134128add1f0555c28b5124a08654af541450e802b72c4d766f` | 11417 | `fnd/w3b` `drafts/w3b/evidence/gates-after/intent_rails.verdict.json` | the w3b commit of `fnd/r8int5` (gen_sch_b.py, the registry notes, DECOUPLING.md section 10) |
| `w3b/evidence/gates-after/pin_map_lands.log` | `fadc2507340704ce35b4f2a6ea2236babb202fdae940b0ec4d2abe9c2cd8e6f9` | 221 | `fnd/w3b` `drafts/w3b/evidence/gates-after/pin_map_lands.log` | the w3b commit of `fnd/r8int5` (gen_sch_b.py, the registry notes, DECOUPLING.md section 10) |
| `w3b/evidence/gates-after/pin_map_lands_b.verdict.json` | `edb38adb1b87d0a54284465478eb83f18c1ca704f53768b886334271723347a3` | 1458 | `fnd/w3b` `drafts/w3b/evidence/gates-after/pin_map_lands_b.verdict.json` | the w3b commit of `fnd/r8int5` (gen_sch_b.py, the registry notes, DECOUPLING.md section 10) |
| `w3b/evidence/gates-after/port_protect.log` | `b5a5d078f995486a8ea0346899e7f2c196dcbfd0b454762aaa78398945abb047` | 1538 | `fnd/w3b` `drafts/w3b/evidence/gates-after/port_protect.log` | the w3b commit of `fnd/r8int5` (gen_sch_b.py, the registry notes, DECOUPLING.md section 10) |
| `w3b/evidence/gates-after/port_protect.verdict.json` | `ead3d9a308d4902d2358870a94c3843eab4fc1cc0c728f87b424ccfce993db79` | 1725 | `fnd/w3b` `drafts/w3b/evidence/gates-after/port_protect.verdict.json` | the w3b commit of `fnd/r8int5` (gen_sch_b.py, the registry notes, DECOUPLING.md section 10) |
| `w3b/evidence/gates-after/port_protect_b.verdict.json` | `d185f96fa797322cc417d3933953da09b36a1d4fb3650d9fc3a2e7a23c9225ea` | 1804 | `fnd/w3b` `drafts/w3b/evidence/gates-after/port_protect_b.verdict.json` | the w3b commit of `fnd/r8int5` (gen_sch_b.py, the registry notes, DECOUPLING.md section 10) |
| `w3b/evidence/gates-after/power_path.log` | `833645aa7793ff892647f8981b7cc432b896b9f8bb00d60434422e6c06eb884c` | 1155 | `fnd/w3b` `drafts/w3b/evidence/gates-after/power_path.log` | the w3b commit of `fnd/r8int5` (gen_sch_b.py, the registry notes, DECOUPLING.md section 10) |
| `w3b/evidence/gates-after/power_path.verdict.json` | `f140981cadb7ecfec357bcff51cfcd2ffa08a97a4991436f34ff175b6291aa9c` | 1185 | `fnd/w3b` `drafts/w3b/evidence/gates-after/power_path.verdict.json` | the w3b commit of `fnd/r8int5` (gen_sch_b.py, the registry notes, DECOUPLING.md section 10) |
| `w3b/evidence/gates-after/power_sequence.log` | `4f26e89690f6c5c222190f5a45faf1671785cf298aa75abace09a84699c39373` | 4460 | `fnd/w3b` `drafts/w3b/evidence/gates-after/power_sequence.log` | the w3b commit of `fnd/r8int5` (gen_sch_b.py, the registry notes, DECOUPLING.md section 10) |
| `w3b/evidence/gates-after/power_sequence.verdict.json` | `e8c06fae56242da6933bc8b19da4d657b8f84e634456f22c134fb98edf4abab2` | 1745 | `fnd/w3b` `drafts/w3b/evidence/gates-after/power_sequence.verdict.json` | the w3b commit of `fnd/r8int5` (gen_sch_b.py, the registry notes, DECOUPLING.md section 10) |
| `w3b/evidence/gates-after/review_nets.log` | `edf934ae4774c56ea149d2bb6366a73614cff81fd21c06efacda5ca010a7e9b9` | 1434 | `fnd/w3b` `drafts/w3b/evidence/gates-after/review_nets.log` | the w3b commit of `fnd/r8int5` (gen_sch_b.py, the registry notes, DECOUPLING.md section 10) |
| `w3b/evidence/gates-after/safe_lines.log` | `34a4483a386c1f3ce5799d4c88a45354c3c94440990cbb9c5261cfae3e82b6f7` | 1057 | `fnd/w3b` `drafts/w3b/evidence/gates-after/safe_lines.log` | the w3b commit of `fnd/r8int5` (gen_sch_b.py, the registry notes, DECOUPLING.md section 10) |
| `w3b/evidence/gates-after/safe_lines.verdict.json` | `42591e3b1851539405fc94350e6b222140411c58d8581f440766ffbc19cff828` | 2468 | `fnd/w3b` `drafts/w3b/evidence/gates-after/safe_lines.verdict.json` | the w3b commit of `fnd/r8int5` (gen_sch_b.py, the registry notes, DECOUPLING.md section 10) |
| `w3b/evidence/gates-after/safe_lines_b.verdict.json` | `1ce5b34a4c6492d66545a4484e51dc75814d5e877fa59441755efed5b6d51b78` | 2470 | `fnd/w3b` `drafts/w3b/evidence/gates-after/safe_lines_b.verdict.json` | the w3b commit of `fnd/r8int5` (gen_sch_b.py, the registry notes, DECOUPLING.md section 10) |
| `w3b/evidence/gates-after/tx_inhibit.log` | `921c66582315c270867ff43aabafbd4c8434a83decc1d7f24674ad52f94a7182` | 18435 | `fnd/w3b` `drafts/w3b/evidence/gates-after/tx_inhibit.log` | the w3b commit of `fnd/r8int5` (gen_sch_b.py, the registry notes, DECOUPLING.md section 10) |
| `w3b/evidence/gates-before/check_contracts.log` | `757343a55caf14774bf371cfc0e0cbf2474ac45b4461f9560fa5b7819b89b2d3` | 24221 | `fnd/w3b` `drafts/w3b/evidence/gates-before/check_contracts.log` | the w3b commit of `fnd/r8int5` (gen_sch_b.py, the registry notes, DECOUPLING.md section 10) |
| `w3b/evidence/gates-before/check_contracts.verdict.json` | `7022c36389400ce153b41fc315f6e7f6f1748bef395a80ee6bd297b7d5caec61` | 2941 | `fnd/w3b` `drafts/w3b/evidence/gates-before/check_contracts.verdict.json` | the w3b commit of `fnd/r8int5` (gen_sch_b.py, the registry notes, DECOUPLING.md section 10) |
| `w3b/evidence/gates-before/check_contracts_a.verdict.json` | `81c15f908f4f92e3b88981dfd54ce85f1e7d20a122af89ea79d52dadda36a44d` | 2693 | `fnd/w3b` `drafts/w3b/evidence/gates-before/check_contracts_a.verdict.json` | the w3b commit of `fnd/r8int5` (gen_sch_b.py, the registry notes, DECOUPLING.md section 10) |
| `w3b/evidence/gates-before/check_contracts_b.verdict.json` | `af9553cbc749de619f9eaed520c86d442dee095bc560647824fc935d5b08de1f` | 2438 | `fnd/w3b` `drafts/w3b/evidence/gates-before/check_contracts_b.verdict.json` | the w3b commit of `fnd/r8int5` (gen_sch_b.py, the registry notes, DECOUPLING.md section 10) |
| `w3b/evidence/gates-before/check_contracts_c.verdict.json` | `d39c8ba3e50e6977f32fc6ff2973ce874f79b84dd411de4257011e489b86ae89` | 2436 | `fnd/w3b` `drafts/w3b/evidence/gates-before/check_contracts_c.verdict.json` | the w3b commit of `fnd/r8int5` (gen_sch_b.py, the registry notes, DECOUPLING.md section 10) |
| `w3b/evidence/gates-before/check_contracts_d.verdict.json` | `902d87d5413bd6d591574543b3268d60c442b923d2409e1c14fc9fe3172f4bf8` | 2438 | `fnd/w3b` `drafts/w3b/evidence/gates-before/check_contracts_d.verdict.json` | the w3b commit of `fnd/r8int5` (gen_sch_b.py, the registry notes, DECOUPLING.md section 10) |
| `w3b/evidence/gates-before/check_contracts_e.verdict.json` | `9e9c912b2d50e11d91156a94b84611753d007b501136d80a5ac3b29d9ad06c36` | 2165 | `fnd/w3b` `drafts/w3b/evidence/gates-before/check_contracts_e.verdict.json` | the w3b commit of `fnd/r8int5` (gen_sch_b.py, the registry notes, DECOUPLING.md section 10) |
| `w3b/evidence/gates-before/check_contracts_p.verdict.json` | `ac861e6abefb13d9a88a29741f441d7802ca66e9c321fd13aaffc56020e67037` | 1906 | `fnd/w3b` `drafts/w3b/evidence/gates-before/check_contracts_p.verdict.json` | the w3b commit of `fnd/r8int5` (gen_sch_b.py, the registry notes, DECOUPLING.md section 10) |
| `w3b/evidence/gates-before/clock_check.log` | `0f52220d2d6615664516b6b28aec64c63f14908fdcb00e265e5eb342c3194e8f` | 1386 | `fnd/w3b` `drafts/w3b/evidence/gates-before/clock_check.log` | the w3b commit of `fnd/r8int5` (gen_sch_b.py, the registry notes, DECOUPLING.md section 10) |
| `w3b/evidence/gates-before/clock_check.verdict.json` | `9a328bd1172737f7f5678f7de963d4a22247587c62f772fd1e6687c2f7f55f9f` | 1258 | `fnd/w3b` `drafts/w3b/evidence/gates-before/clock_check.verdict.json` | the w3b commit of `fnd/r8int5` (gen_sch_b.py, the registry notes, DECOUPLING.md section 10) |
| `w3b/evidence/gates-before/derate.log` | `b65558db711189ad52f0c5c8d800678a81ad1e087a316e2292ef323034c039bf` | 595 | `fnd/w3b` `drafts/w3b/evidence/gates-before/derate.log` | the w3b commit of `fnd/r8int5` (gen_sch_b.py, the registry notes, DECOUPLING.md section 10) |
| `w3b/evidence/gates-before/derate.verdict.json` | `44350aa7072b04766410b6052f985d6ef1ce1f3f82d7db993cb9a57f5104886c` | 1293 | `fnd/w3b` `drafts/w3b/evidence/gates-before/derate.verdict.json` | the w3b commit of `fnd/r8int5` (gen_sch_b.py, the registry notes, DECOUPLING.md section 10) |
| `w3b/evidence/gates-before/edge_length.log` | `f912f5d727a1213666f6d0597770f4febb627a042f3d86cc632b3fa68802445c` | 12727 | `fnd/w3b` `drafts/w3b/evidence/gates-before/edge_length.log` | the w3b commit of `fnd/r8int5` (gen_sch_b.py, the registry notes, DECOUPLING.md section 10) |
| `w3b/evidence/gates-before/edge_length.verdict.json` | `18544c51deb1b9d97abcf7ee9664166dba67bfc2f1a90719f739f49a70abcac0` | 27396 | `fnd/w3b` `drafts/w3b/evidence/gates-before/edge_length.verdict.json` | the w3b commit of `fnd/r8int5` (gen_sch_b.py, the registry notes, DECOUPLING.md section 10) |
| `w3b/evidence/gates-before/energy_chain.log` | `9ec7be1be121756e26bf2c06366ce9c0b2fdce213c26b63f4c1e9d395080bccd` | 2579 | `fnd/w3b` `drafts/w3b/evidence/gates-before/energy_chain.log` | the w3b commit of `fnd/r8int5` (gen_sch_b.py, the registry notes, DECOUPLING.md section 10) |
| `w3b/evidence/gates-before/energy_chain.verdict.json` | `2457e4ffd133d33a1e9b2c59c4c54d8b1020ae5534b36bc0c0863a43abc5ff78` | 2479 | `fnd/w3b` `drafts/w3b/evidence/gates-before/energy_chain.verdict.json` | the w3b commit of `fnd/r8int5` (gen_sch_b.py, the registry notes, DECOUPLING.md section 10) |
| `w3b/evidence/gates-before/energy_chain_a.verdict.json` | `7a7c4ef73214efb151f13f8b1c1360794c39c9cb634407fbf9cfbafd450d9cbc` | 1750 | `fnd/w3b` `drafts/w3b/evidence/gates-before/energy_chain_a.verdict.json` | the w3b commit of `fnd/r8int5` (gen_sch_b.py, the registry notes, DECOUPLING.md section 10) |
| `w3b/evidence/gates-before/energy_chain_b.verdict.json` | `659c8d456e87a8c0dd5f4f5bf2a4da649849b0ce48f433fe11d257e252bcf026` | 1612 | `fnd/w3b` `drafts/w3b/evidence/gates-before/energy_chain_b.verdict.json` | the w3b commit of `fnd/r8int5` (gen_sch_b.py, the registry notes, DECOUPLING.md section 10) |
| `w3b/evidence/gates-before/energy_chain_e.verdict.json` | `27da3c3e18a1ecb24db6170dc60a04e6b6a3ce3d4d7990901fa9a714dbe2ea2a` | 1750 | `fnd/w3b` `drafts/w3b/evidence/gates-before/energy_chain_e.verdict.json` | the w3b commit of `fnd/r8int5` (gen_sch_b.py, the registry notes, DECOUPLING.md section 10) |
| `w3b/evidence/gates-before/energy_chain_e5.verdict.json` | `a05a9fbf18b25de4d7b13dc8aefb4b0a8ecb87854d0ff5d5d4926ccdd4257f09` | 1558 | `fnd/w3b` `drafts/w3b/evidence/gates-before/energy_chain_e5.verdict.json` | the w3b commit of `fnd/r8int5` (gen_sch_b.py, the registry notes, DECOUPLING.md section 10) |
| `w3b/evidence/gates-before/energy_chain_p.verdict.json` | `ef32c9b14e0305891bfafeb5e3f34ba303b3b43d0113517a4476291da4f165ad` | 1606 | `fnd/w3b` `drafts/w3b/evidence/gates-before/energy_chain_p.verdict.json` | the w3b commit of `fnd/r8int5` (gen_sch_b.py, the registry notes, DECOUPLING.md section 10) |
| `w3b/evidence/gates-before/ground_system.log` | `5eeea039935262ffa6b999d5039b902d25598faf4800c0f04fa88bf1276f521a` | 381 | `fnd/w3b` `drafts/w3b/evidence/gates-before/ground_system.log` | the w3b commit of `fnd/r8int5` (gen_sch_b.py, the registry notes, DECOUPLING.md section 10) |
| `w3b/evidence/gates-before/ground_system.verdict.json` | `fded0efa127769570294cbb1f9fa31cfb11ac0e2edcfb9fd2529b718b4df6094` | 1264 | `fnd/w3b` `drafts/w3b/evidence/gates-before/ground_system.verdict.json` | the w3b commit of `fnd/r8int5` (gen_sch_b.py, the registry notes, DECOUPLING.md section 10) |
| `w3b/evidence/gates-before/inhibit_chain_a.verdict.json` | `e66b2b9bc112d28e78d58356377e2333bdc7a1cc3609d3bc1525ebeffa10ec41` | 4270 | `fnd/w3b` `drafts/w3b/evidence/gates-before/inhibit_chain_a.verdict.json` | the w3b commit of `fnd/r8int5` (gen_sch_b.py, the registry notes, DECOUPLING.md section 10) |
| `w3b/evidence/gates-before/inhibit_chain_b.verdict.json` | `00423b8c7400041aa40b6d30fb22843595dea4c5b8b535aabb1304735e05df5e` | 5382 | `fnd/w3b` `drafts/w3b/evidence/gates-before/inhibit_chain_b.verdict.json` | the w3b commit of `fnd/r8int5` (gen_sch_b.py, the registry notes, DECOUPLING.md section 10) |
| `w3b/evidence/gates-before/inhibit_chain_c.verdict.json` | `01eef7200b85b002f0b3c38c5eb94a098c2ffb279d56f1641e546c54461f12a1` | 3802 | `fnd/w3b` `drafts/w3b/evidence/gates-before/inhibit_chain_c.verdict.json` | the w3b commit of `fnd/r8int5` (gen_sch_b.py, the registry notes, DECOUPLING.md section 10) |
| `w3b/evidence/gates-before/inhibit_chain_d.verdict.json` | `e05da462c63f80a09d5137cac0663e4869ea082aab4bd9f34d480c524e951f66` | 3631 | `fnd/w3b` `drafts/w3b/evidence/gates-before/inhibit_chain_d.verdict.json` | the w3b commit of `fnd/r8int5` (gen_sch_b.py, the registry notes, DECOUPLING.md section 10) |
| `w3b/evidence/gates-before/inhibit_chain_e.verdict.json` | `6b11cbbd5fe71cd0ee207c7fa3b964f63cd8416cf0653547364d840d51211a1f` | 2901 | `fnd/w3b` `drafts/w3b/evidence/gates-before/inhibit_chain_e.verdict.json` | the w3b commit of `fnd/r8int5` (gen_sch_b.py, the registry notes, DECOUPLING.md section 10) |
| `w3b/evidence/gates-before/inhibit_chain_p.verdict.json` | `0491d6683892ff0d0234f12c07261f87890a5581dcc358ce8d7086076795bb86` | 2644 | `fnd/w3b` `drafts/w3b/evidence/gates-before/inhibit_chain_p.verdict.json` | the w3b commit of `fnd/r8int5` (gen_sch_b.py, the registry notes, DECOUPLING.md section 10) |
| `w3b/evidence/gates-before/intent_rails.log` | `7b85e395fe43fd8fe2c0419d16153232d96e72b414a6dfdc28e77b9c0b24da5d` | 21059 | `fnd/w3b` `drafts/w3b/evidence/gates-before/intent_rails.log` | the w3b commit of `fnd/r8int5` (gen_sch_b.py, the registry notes, DECOUPLING.md section 10) |
| `w3b/evidence/gates-before/intent_rails.verdict.json` | `e83c1c592f914a6ae2e130cd905deb84b8bddf74e97433111437ea06b819e446` | 14394 | `fnd/w3b` `drafts/w3b/evidence/gates-before/intent_rails.verdict.json` | the w3b commit of `fnd/r8int5` (gen_sch_b.py, the registry notes, DECOUPLING.md section 10) |
| `w3b/evidence/gates-before/pin_map_lands.log` | `2c367ca833fdd202038bae999580f8e2246645b970cb1d31d414c1f855d11474` | 221 | `fnd/w3b` `drafts/w3b/evidence/gates-before/pin_map_lands.log` | the w3b commit of `fnd/r8int5` (gen_sch_b.py, the registry notes, DECOUPLING.md section 10) |
| `w3b/evidence/gates-before/pin_map_lands_b.verdict.json` | `c81ed22d4f9c6e4548c9f267bdfec41ae3d5b87c0a0ce024aa3c50b0e3936481` | 1452 | `fnd/w3b` `drafts/w3b/evidence/gates-before/pin_map_lands_b.verdict.json` | the w3b commit of `fnd/r8int5` (gen_sch_b.py, the registry notes, DECOUPLING.md section 10) |
| `w3b/evidence/gates-before/port_protect.log` | `b5a5d078f995486a8ea0346899e7f2c196dcbfd0b454762aaa78398945abb047` | 1538 | `fnd/w3b` `drafts/w3b/evidence/gates-before/port_protect.log` | the w3b commit of `fnd/r8int5` (gen_sch_b.py, the registry notes, DECOUPLING.md section 10) |
| `w3b/evidence/gates-before/port_protect.verdict.json` | `a5651ed01123f4d7c791add5073d681d50697d6bf60ec646dc9ec6d74542b323` | 1719 | `fnd/w3b` `drafts/w3b/evidence/gates-before/port_protect.verdict.json` | the w3b commit of `fnd/r8int5` (gen_sch_b.py, the registry notes, DECOUPLING.md section 10) |
| `w3b/evidence/gates-before/port_protect_b.verdict.json` | `772368e6e62ab07a272953118b7597ef842d31467ddb3c3846e4ab90e7a4742f` | 1798 | `fnd/w3b` `drafts/w3b/evidence/gates-before/port_protect_b.verdict.json` | the w3b commit of `fnd/r8int5` (gen_sch_b.py, the registry notes, DECOUPLING.md section 10) |
| `w3b/evidence/gates-before/power_path.log` | `8b41bae25f77c6f12d4c64200ee5e292e72f26484524785e2cdb4f267c077fb6` | 1155 | `fnd/w3b` `drafts/w3b/evidence/gates-before/power_path.log` | the w3b commit of `fnd/r8int5` (gen_sch_b.py, the registry notes, DECOUPLING.md section 10) |
| `w3b/evidence/gates-before/power_path.verdict.json` | `f9e729d1022c7be7a6141f4e7a6af3b97db8ffe69443a8f7d8f203645a44aa1c` | 1179 | `fnd/w3b` `drafts/w3b/evidence/gates-before/power_path.verdict.json` | the w3b commit of `fnd/r8int5` (gen_sch_b.py, the registry notes, DECOUPLING.md section 10) |
| `w3b/evidence/gates-before/power_sequence.log` | `4d2204b9f802a26e71b96d0eef8b0d0547917eb03aa3e3bb5d8e591537f57af7` | 3460 | `fnd/w3b` `drafts/w3b/evidence/gates-before/power_sequence.log` | the w3b commit of `fnd/r8int5` (gen_sch_b.py, the registry notes, DECOUPLING.md section 10) |
| `w3b/evidence/gates-before/power_sequence.verdict.json` | `7d3eed3351c8129bf4b406ce9fe36cd22c22d2b4a334b0efc2d5aa3a76021e2a` | 1738 | `fnd/w3b` `drafts/w3b/evidence/gates-before/power_sequence.verdict.json` | the w3b commit of `fnd/r8int5` (gen_sch_b.py, the registry notes, DECOUPLING.md section 10) |
| `w3b/evidence/gates-before/review_nets.log` | `078d037349c3d4dd427d3ec0acedc18ae2de8606dc07796b612bcb2d3106e492` | 1664 | `fnd/w3b` `drafts/w3b/evidence/gates-before/review_nets.log` | the w3b commit of `fnd/r8int5` (gen_sch_b.py, the registry notes, DECOUPLING.md section 10) |
| `w3b/evidence/gates-before/safe_lines.log` | `34a4483a386c1f3ce5799d4c88a45354c3c94440990cbb9c5261cfae3e82b6f7` | 1057 | `fnd/w3b` `drafts/w3b/evidence/gates-before/safe_lines.log` | the w3b commit of `fnd/r8int5` (gen_sch_b.py, the registry notes, DECOUPLING.md section 10) |
| `w3b/evidence/gates-before/tx_inhibit.log` | `921c66582315c270867ff43aabafbd4c8434a83decc1d7f24674ad52f94a7182` | 18435 | `fnd/w3b` `drafts/w3b/evidence/gates-before/tx_inhibit.log` | the w3b commit of `fnd/r8int5` (gen_sch_b.py, the registry notes, DECOUPLING.md section 10) |
| `w3b/evidence/gates-box/base/erc_gate.log` | `3b25e5c57e3c082aac620186ef44f8a1c5a080b429541525b36c4bcfc0d5a850` | 729 | `fnd/w3b` `drafts/w3b/evidence/gates-box/base/erc_gate.log` | the w3b commit of `fnd/r8int5` (gen_sch_b.py, the registry notes, DECOUPLING.md section 10) |
| `w3b/evidence/gates-box/base/intent_board.log` | `17a1fa808b9646fdeedba3154b6a5ffa9b25e19db32162b0e8649a772ff30d2b` | 193537 | `fnd/w3b` `drafts/w3b/evidence/gates-box/base/intent_board.log` | the w3b commit of `fnd/r8int5` (gen_sch_b.py, the registry notes, DECOUPLING.md section 10) |
| `w3b/evidence/gates-box/base/intent_checks.verdict.json` | `ab558bf0e17e00c1f0f0c4f19f611bb958a20e467c7a5330ae40055845a0f734` | 5138 | `fnd/w3b` `drafts/w3b/evidence/gates-box/base/intent_checks.verdict.json` | the w3b commit of `fnd/r8int5` (gen_sch_b.py, the registry notes, DECOUPLING.md section 10) |
| `w3b/evidence/gates-box/base/intent_decoupling.verdict.json` | `858f5f8db0f4338c872c960f9a5767ca9ef0b6044abb316d84e49cfff71b5e38` | 2675 | `fnd/w3b` `drafts/w3b/evidence/gates-box/base/intent_decoupling.verdict.json` | the w3b commit of `fnd/r8int5` (gen_sch_b.py, the registry notes, DECOUPLING.md section 10) |
| `w3b/evidence/gates-box/base/intent_other.verdict.json` | `83c30137bdee9a9300ffad74d285c0a075544c70e11435711757ce6a9c9c1180` | 1668 | `fnd/w3b` `drafts/w3b/evidence/gates-box/base/intent_other.verdict.json` | the w3b commit of `fnd/r8int5` (gen_sch_b.py, the registry notes, DECOUPLING.md section 10) |
| `w3b/evidence/gates-box/base/intent_rails.verdict.json` | `55065cf73cd5f8c3b805b96e5f0a123f0646605e6e706c154efd4a9310417f6d` | 14434 | `fnd/w3b` `drafts/w3b/evidence/gates-box/base/intent_rails.verdict.json` | the w3b commit of `fnd/r8int5` (gen_sch_b.py, the registry notes, DECOUPLING.md section 10) |
| `w3b/evidence/gates-box/base/intent_return_path.verdict.json` | `0bb420a3c6916e7098e64feab270d2d51c0224322786d48491b7c7d727c4f439` | 2000 | `fnd/w3b` `drafts/w3b/evidence/gates-box/base/intent_return_path.verdict.json` | the w3b commit of `fnd/r8int5` (gen_sch_b.py, the registry notes, DECOUPLING.md section 10) |
| `w3b/evidence/gates-box/base/intent_return_via.verdict.json` | `d2066e5ff27794a4b2c850ba84414c06168cf4e3d23e349c80ed7ef4bc2f699d` | 2160 | `fnd/w3b` `drafts/w3b/evidence/gates-box/base/intent_return_via.verdict.json` | the w3b commit of `fnd/r8int5` (gen_sch_b.py, the registry notes, DECOUPLING.md section 10) |
| `w3b/evidence/gates-box/cand/erc_gate.log` | `77a8841ce7b38f3d1ecb5b8da45bbd9b288f13a66136d6a51f961820f30ffb5a` | 729 | `fnd/w3b` `drafts/w3b/evidence/gates-box/cand/erc_gate.log` | the w3b commit of `fnd/r8int5` (gen_sch_b.py, the registry notes, DECOUPLING.md section 10) |
| `w3b/evidence/gates-box/cand/intent_board.log` | `f27d5075fa5b534929a8cf15949e16e1cc451dab8d7f6583f9152e9e2d53df1f` | 190686 | `fnd/w3b` `drafts/w3b/evidence/gates-box/cand/intent_board.log` | the w3b commit of `fnd/r8int5` (gen_sch_b.py, the registry notes, DECOUPLING.md section 10) |
| `w3b/evidence/gates-box/cand/intent_checks.verdict.json` | `8bd6395a2cd7f7e1ce42a45c14f4141d962c194f6f2c8f5d096535a1796de6ed` | 5138 | `fnd/w3b` `drafts/w3b/evidence/gates-box/cand/intent_checks.verdict.json` | the w3b commit of `fnd/r8int5` (gen_sch_b.py, the registry notes, DECOUPLING.md section 10) |
| `w3b/evidence/gates-box/cand/intent_decoupling.verdict.json` | `09d2cf0e239bacd16458927620f87a64fd28b86e12e4ec76482d108f87427b8c` | 2675 | `fnd/w3b` `drafts/w3b/evidence/gates-box/cand/intent_decoupling.verdict.json` | the w3b commit of `fnd/r8int5` (gen_sch_b.py, the registry notes, DECOUPLING.md section 10) |
| `w3b/evidence/gates-box/cand/intent_other.verdict.json` | `29a1f90f9806cf1a86c7f753c39ec4905bafb226278f1183a997343c902023a0` | 1765 | `fnd/w3b` `drafts/w3b/evidence/gates-box/cand/intent_other.verdict.json` | the w3b commit of `fnd/r8int5` (gen_sch_b.py, the registry notes, DECOUPLING.md section 10) |
| `w3b/evidence/gates-box/cand/intent_rails.verdict.json` | `8c78808ddee1c69989990d03d81df90628ee361228bbabc45cc649223f89c2ef` | 11451 | `fnd/w3b` `drafts/w3b/evidence/gates-box/cand/intent_rails.verdict.json` | the w3b commit of `fnd/r8int5` (gen_sch_b.py, the registry notes, DECOUPLING.md section 10) |
| `w3b/evidence/gates-box/cand/intent_return_path.verdict.json` | `223ff58b9cbc3bdb28858bbbed12e06e6751971e526586daab5e353da311fbb1` | 2000 | `fnd/w3b` `drafts/w3b/evidence/gates-box/cand/intent_return_path.verdict.json` | the w3b commit of `fnd/r8int5` (gen_sch_b.py, the registry notes, DECOUPLING.md section 10) |
| `w3b/evidence/gates-box/cand/intent_return_via.verdict.json` | `f8219f01a9e807567f5f612fe24ecc10becbe670a48bb3c2b0b6af8eaa749d48` | 2160 | `fnd/w3b` `drafts/w3b/evidence/gates-box/cand/intent_return_via.verdict.json` | the w3b commit of `fnd/r8int5` (gen_sch_b.py, the registry notes, DECOUPLING.md section 10) |
| `w3b/evidence/jlc-certify-w3b.txt` | `75db55ee972ec8e69656689093607ca0d450d089c988b92d6805d96076092b3c` | 1017 | `fnd/w3b` `drafts/w3b/evidence/jlc-certify-w3b.txt` | the w3b commit of `fnd/r8int5` (gen_sch_b.py, the registry notes, DECOUPLING.md section 10) |
| `w3b/evidence/pwr001-after.txt` | `0e95f98d978b40574e0e89f9f92b9465fa1fea4124ca2fa7a7175043343ef4ac` | 16693 | `fnd/w3b` `drafts/w3b/evidence/pwr001-after.txt` | the w3b commit of `fnd/r8int5` (gen_sch_b.py, the registry notes, DECOUPLING.md section 10) |
| `w3b/evidence/pwr001-before.txt` | `62f59401245d22517c6b04e09a81f4f80d1bbef65a86f285fcd986971676433f` | 21052 | `fnd/w3b` `drafts/w3b/evidence/pwr001-before.txt` | the w3b commit of `fnd/r8int5` (gen_sch_b.py, the registry notes, DECOUPLING.md section 10) |
| `w3b/evidence/registry-patch-preview.diff` | `b55ac6aab7d0d0612f66464e83dac1f49d05ba9edd868b84f49389d2dac25add` | 30840 | `fnd/w3b` `drafts/w3b/evidence/registry-patch-preview.diff` | the w3b commit of `fnd/r8int5` (gen_sch_b.py, the registry notes, DECOUPLING.md section 10) |
| `w3b/evidence/requirements-check-after-patch.txt` | `acbfd2c0c3c85674290707b6ccbf8c87415c6ec6e6bf6a79b439966e31877196` | 1355 | `fnd/w3b` `drafts/w3b/evidence/requirements-check-after-patch.txt` | the w3b commit of `fnd/r8int5` (gen_sch_b.py, the registry notes, DECOUPLING.md section 10) |
| `w3b/evidence/requirements-check-before-patch.txt` | `c7664709ab685b4a83c3ff9167bc81a8320de82a3763ccdf9833301385472c11` | 4343 | `fnd/w3b` `drafts/w3b/evidence/requirements-check-before-patch.txt` | the w3b commit of `fnd/r8int5` (gen_sch_b.py, the registry notes, DECOUPLING.md section 10) |
| `w3b/evidence/stray-safe-lines/safe_lines.verdict.json` | `336625732b828d13147603b3ae4caeee3a0f229e266cab6c5275735af452eb69` | 2468 | `fnd/w3b` `drafts/w3b/evidence/stray-safe-lines/safe_lines.verdict.json` | the w3b commit of `fnd/r8int5` (gen_sch_b.py, the registry notes, DECOUPLING.md section 10) |
| `w3b/evidence/stray-safe-lines/safe_lines_b.verdict.json` | `156529a807b3d1b9ed2726a8ad32ae6368a5fb93abf1946123bae8b3b0c1d7db` | 2470 | `fnd/w3b` `drafts/w3b/evidence/stray-safe-lines/safe_lines_b.verdict.json` | the w3b commit of `fnd/r8int5` (gen_sch_b.py, the registry notes, DECOUPLING.md section 10) |
| `w3b/expected_w3b.json` | `1b2c50bbfad8ea5e994b0138edf97af6c69ccd37a486664f81b04c452e9f8a82` | 1826 | `fnd/w3b` `drafts/w3b/expected_w3b.json` | the w3b commit of `fnd/r8int5` (gen_sch_b.py, the registry notes, DECOUPLING.md section 10) |
| `w3b/page-drafts.md` | `f322b3f3e5140b201521f9fd7120a23de8bf9a73c657d6c721f37b2d84606aca` | 4831 | `fnd/w3b` `drafts/w3b/page-drafts.md` | the w3b commit of `fnd/r8int5` (gen_sch_b.py, the registry notes, DECOUPLING.md section 10) |
| `w3b/page_drafts_r8int5.py` | `6c9eb5d9af5007c21b1641b30ae0b6c868f392477139ba0f3f4c5d80f1639e9e` | 6278 | the r8int5 integrator (`page_drafts_r8int5.py`) | the w3b commit of `fnd/r8int5` (gen_sch_b.py, the registry notes, DECOUPLING.md section 10) |
| `w3b/rebind_w3b.py` | `df8178c64fffcce5715dac85f63464eddb62fbad3a501328d357465a6906c41a` | 1242 | the r8int5 integrator (`rebind_w3b.py`) | the w3b commit of `fnd/r8int5` (gen_sch_b.py, the registry notes, DECOUPLING.md section 10) |
| `w3b/sources-entries.yaml` | `4cced32f87af88ac62c1d7b2eda063207cd825af38caa30adaa7d9510c6e79dd` | 1640 | `fnd/w3b` `drafts/w3b/sources-entries.yaml` | the w3b commit of `fnd/r8int5` (gen_sch_b.py, the registry notes, DECOUPLING.md section 10) |
| `w3b/tools/cmp_classes.py` | `04ee546425b8baa4c14d1c251fc9697daa44b5ff8c3d5524abec6244b245628b` | 3052 | `fnd/w3b` `drafts/w3b/tools/cmp_classes.py` | the w3b commit of `fnd/r8int5` (gen_sch_b.py, the registry notes, DECOUPLING.md section 10) |
| `w3b/tools/findq.py` | `1fbcf9f26923915a41f0d74983c18477934cd02a3e4f970611983fa6d3f69e32` | 596 | `fnd/w3b` `drafts/w3b/tools/findq.py` | the w3b commit of `fnd/r8int5` (gen_sch_b.py, the registry notes, DECOUPLING.md section 10) |
| `w3b/tools/gates.sh` | `f0efabc43b8c0c27d302c2aeab094cd0905fc2c20bba0082d1a3fa5068e809ef` | 1792 | `fnd/w3b` `drafts/w3b/tools/gates.sh` | the w3b commit of `fnd/r8int5` (gen_sch_b.py, the registry notes, DECOUPLING.md section 10) |
| `w3b/tools/rename_check.py` | `fb9734d98c9fc7c24d28fdce5ebad3b4bfd10d80dad8fc960b1c2a6f95fdb7df` | 1570 | `fnd/w3b` `drafts/w3b/tools/rename_check.py` | the w3b commit of `fnd/r8int5` (gen_sch_b.py, the registry notes, DECOUPLING.md section 10) |
| `w3b/tools/w3b_box.sh` | `a306d22531be0d03f664059f3142ab63ddf032d3bbe5408a359975f6966283f0` | 10155 | `fnd/w3b` `drafts/w3b/tools/w3b_box.sh` | the w3b commit of `fnd/r8int5` (gen_sch_b.py, the registry notes, DECOUPLING.md section 10) |
| `w3b/w3b-decisions.md` | `ae15bca76d04120c703a176b9e509c712c7a29c49113e048f2c4947c7ac9d620` | 12552 | `fnd/w3b` `drafts/w3b/w3b-decisions.md` | the w3b commit of `fnd/r8int5` (gen_sch_b.py, the registry notes, DECOUPLING.md section 10) |
| `w3de/EQ16-dock-vin-raw.md` | `00805acbb8f97d733c8638cb8ba75dd852c062618e7caec38cf260065983c364` | 10605 | `fnd/w3de` `drafts/w3de/EQ16-dock-vin-raw.md` | the w3de commit of `fnd/r8int5` (the registry notes, IF-AE-DOCK, gen_sch_a.py's EQ-16 comment) |
| `w3de/README.md` | `7eebcc9f0414f0aba4bdca60606899827a2758f53af9d46873f716823fffe06b` | 8647 | `fnd/w3de` `drafts/w3de/README.md` | the w3de commit of `fnd/r8int5` (the registry notes, IF-AE-DOCK, gen_sch_a.py's EQ-16 comment) |
| `w3de/apply_registry.py` | `0f11c72ad4f4811e16e026668719069a6b2446659f212f57d252c10a29e32c3b` | 25091 | `fnd/w3de` `drafts/w3de/apply_registry.py` | the w3de commit of `fnd/r8int5` (the registry notes, IF-AE-DOCK, gen_sch_a.py's EQ-16 comment) |
| `w3de/apply_registry_r8int5.py` | `421389cadba95f450ccf991204e487d67184e1c9cf9b6ebe7f4128e3c7dbdd0f` | 10362 | the r8int5 integrator (`apply_registry_r8int5.py`) | the w3de commit of `fnd/r8int5` (the registry notes, IF-AE-DOCK, gen_sch_a.py's EQ-16 comment) |
| `w3de/architecture_r8int5.py` | `15a8403499f33f8e902261e3d63bdcdb7e9d4d6d333809336f21304bbc4a7dd4` | 3923 | the r8int5 integrator (`architecture_r8int5.py`) | the w3de commit of `fnd/r8int5` (the registry notes, IF-AE-DOCK, gen_sch_a.py's EQ-16 comment) |
| `w3de/coverage_r8int5.py` | `4fb1965a21459018e414be75b8d2b13eb9adcaaf54041ffcffc5f773f90aea9e` | 1359 | the r8int5 integrator (`coverage_r8int5.py`) | the w3de commit of `fnd/r8int5` (the registry notes, IF-AE-DOCK, gen_sch_a.py's EQ-16 comment) |
| `w3de/dock_contacts.py` | `acd932cbb9e31f8f0fd4563fc97d7ece21e0ce531e133040afb911da3c513b41` | 6851 | `fnd/w3de` `drafts/w3de/dock_contacts.py` | the w3de commit of `fnd/r8int5` (the registry notes, IF-AE-DOCK, gen_sch_a.py's EQ-16 comment) |
| `w3de/ecss-6.11-transcription.md` | `a910e757d77bea6ca3646493035160e759a4c0b25b29a9c0d42dc551552b3143` | 2032 | `fnd/w3de` `drafts/w3de/ecss-6.11-transcription.md` | the w3de commit of `fnd/r8int5` (the registry notes, IF-AE-DOCK, gen_sch_a.py's EQ-16 comment) |
| `w3de/ecss_append_r8int5.py` | `56f711f3069d1f4a2423e84a3ad1b4d5531c12456f2a0b3eed1eac89ab2af77e` | 1018 | the r8int5 integrator (`ecss_append_r8int5.py`) | the w3de commit of `fnd/r8int5` (the registry notes, IF-AE-DOCK, gen_sch_a.py's EQ-16 comment) |
| `w3de/eq_r8int5.py` | `b1171f773fadb7d20ee022ea28e416018246073ce403acb8cd5207e7fb3126cd` | 2803 | the r8int5 integrator (`eq_r8int5.py`) | the w3de commit of `fnd/r8int5` (the registry notes, IF-AE-DOCK, gen_sch_a.py's EQ-16 comment) |
| `w3de/fix_bringup_kind_r8int5.py` | `701753ee8334975235b16cb45d8de0afceb17c719fb74f95c64b825066b6443a` | 7511 | the r8int5 integrator (`fix_bringup_kind_r8int5.py`) | the w3de commit of `fnd/r8int5` (the registry notes, IF-AE-DOCK, gen_sch_a.py's EQ-16 comment) |
| `w3de/intent_compare.py` | `e8d3ec656dab92a051b2a75b9ab366441fb5079c59e149a1822dfd418a0ad42e` | 1685 | `fnd/w3de` `drafts/w3de/intent_compare.py` | the w3de commit of `fnd/r8int5` (the registry notes, IF-AE-DOCK, gen_sch_a.py's EQ-16 comment) |
| `w3de/net_compare.py` | `99b78011e0ac94d6c6a740f1b189b93dbe6b58fa231f2cdba5cc1ddb45f24a7a` | 6429 | `fnd/w3de` `drafts/w3de/net_compare.py` | the w3de commit of `fnd/r8int5` (the registry notes, IF-AE-DOCK, gen_sch_a.py's EQ-16 comment) |
| `w3de/parity-r8int5/a-intent_compare-vs-w3a.txt` | `8ebcfa026c95d54be6b55840ec95f646505257557c2929de0506c466981d380c` | 76 | the r8int5 integrator (`parity-r8int5/a-intent_compare-vs-w3a.txt`) | the w3de commit of `fnd/r8int5` (the registry notes, IF-AE-DOCK, gen_sch_a.py's EQ-16 comment) |
| `w3de/parity-r8int5/a-net_compare-vs-w3a.txt` | `88119c1608a8d9575a63a1de71c88f56b2adcd2f43aaf33cef98d8ba8f17250b` | 1062 | the r8int5 integrator (`parity-r8int5/a-net_compare-vs-w3a.txt`) | the w3de commit of `fnd/r8int5` (the registry notes, IF-AE-DOCK, gen_sch_a.py's EQ-16 comment) |
| `w3de/parity-r8int5/a-netcmp-w3a-reader.txt` | `37f0fb8977d25b6bfdcbf9d5902ea9644a51f5d02ca98a98e99ec0657bc29dd3` | 2331 | the r8int5 integrator (`parity-r8int5/a-netcmp-w3a-reader.txt`) | the w3de commit of `fnd/r8int5` (the registry notes, IF-AE-DOCK, gen_sch_a.py's EQ-16 comment) |
| `w3de/parity-r8int5/regen-a.log` | `54261b664f9adf8570bdc2095f44cd09f8f29bf5d2e3d97286ed3817311ea001` | 227 | the r8int5 integrator (`parity-r8int5/regen-a.log`) | the w3de commit of `fnd/r8int5` (the registry notes, IF-AE-DOCK, gen_sch_a.py's EQ-16 comment) |
| `w3de/parity-r8int5/regen-out-a/a/committed/pcb-a-power-bom.csv` | `9b4f486ea0bdc4059f02d49f91fe06a61ce08f9d3a46207711e35cda6639af2b` | 19800 | the r8int5 integrator (`parity-r8int5/regen-out-a/a/committed/pcb-a-power-bom.csv`) | the w3de commit of `fnd/r8int5` (the registry notes, IF-AE-DOCK, gen_sch_a.py's EQ-16 comment) |
| `w3de/parity-r8int5/regen-out-a/a/parity_bom.json` | `b397f81b0e1c2266097e97f90c628224294a06243d3fd41bfd6dcaf86e085f13` | 964 | the r8int5 integrator (`parity-r8int5/regen-out-a/a/parity_bom.json`) | the w3de commit of `fnd/r8int5` (the registry notes, IF-AE-DOCK, gen_sch_a.py's EQ-16 comment) |
| `w3de/parity-r8int5/regen-out-a/a/parity_erc.json` | `f99d994ce7d068d5e091c9c8d39eaf9b86a34a40e70c1c559d6bacf461d21057` | 5896 | the r8int5 integrator (`parity-r8int5/regen-out-a/a/parity_erc.json`) | the w3de commit of `fnd/r8int5` (the registry notes, IF-AE-DOCK, gen_sch_a.py's EQ-16 comment) |
| `w3de/parity-r8int5/regen-out-a/a/parity_intent.json` | `214d3adea5e691ba210564b1565bec561a862212c564d7b33a26efadde7d4b2c` | 79 | the r8int5 integrator (`parity-r8int5/regen-out-a/a/parity_intent.json`) | the w3de commit of `fnd/r8int5` (the registry notes, IF-AE-DOCK, gen_sch_a.py's EQ-16 comment) |
| `w3de/parity-r8int5/regen-out-a/a/parity_netlist.json` | `6db82494cf4df17757a04130d1d5c2e96f1878667f06c51b20ffe0ac90449a7f` | 6545 | the r8int5 integrator (`parity-r8int5/regen-out-a/a/parity_netlist.json`) | the w3de commit of `fnd/r8int5` (the registry notes, IF-AE-DOCK, gen_sch_a.py's EQ-16 comment) |
| `w3de/parity-r8int5/regen-out-a/a/parity_schematic.json` | `7c3974e57d117b568d54ff9bf25b77f4a40c97453747122d9a6efeb9618b5ae4` | 9122 | the r8int5 integrator (`parity-r8int5/regen-out-a/a/parity_schematic.json`) | the w3de commit of `fnd/r8int5` (the registry notes, IF-AE-DOCK, gen_sch_a.py's EQ-16 comment) |
| `w3de/parity-r8int5/regen-out-a/a/regen-pcb-a-power-bom.csv` | `f0eec9a40c1fb30f5fb7567cf4c848e85ec8c71aa8653785f9f05470694eb35d` | 20059 | the r8int5 integrator (`parity-r8int5/regen-out-a/a/regen-pcb-a-power-bom.csv`) | the w3de commit of `fnd/r8int5` (the registry notes, IF-AE-DOCK, gen_sch_a.py's EQ-16 comment) |
| `w3de/parity-r8int5/regen-out-a/a/regen.json` | `2236dca176cf7ba71b42fa64322d83c61cffae7c3c974f45e7f9ecaa1b4a35e3` | 4555 | the r8int5 integrator (`parity-r8int5/regen-out-a/a/regen.json`) | the w3de commit of `fnd/r8int5` (the registry notes, IF-AE-DOCK, gen_sch_a.py's EQ-16 comment) |
| `w3de/parity/a-draft/candidate/intent_compare.txt` | `8ebcfa026c95d54be6b55840ec95f646505257557c2929de0506c466981d380c` | 76 | `fnd/w3de` `drafts/w3de/parity/a-draft/candidate/intent_compare.txt` | the w3de commit of `fnd/r8int5` (the registry notes, IF-AE-DOCK, gen_sch_a.py's EQ-16 comment) |
| `w3de/parity/a-draft/candidate/net_compare.json` | `f68d220fb731a4d69f17f9fa66ec0cb0fe670de0ffe5dbf14179700a2d6bf2c0` | 1222 | `fnd/w3de` `drafts/w3de/parity/a-draft/candidate/net_compare.json` | the w3de commit of `fnd/r8int5` (the registry notes, IF-AE-DOCK, gen_sch_a.py's EQ-16 comment) |
| `w3de/parity/a-draft/candidate/parity_bom.json` | `715b0fd47d781aabc19d515fb7f95d5e111acc1cb365677aa2ab5b4a6658cc65` | 964 | `fnd/w3de` `drafts/w3de/parity/a-draft/candidate/parity_bom.json` | the w3de commit of `fnd/r8int5` (the registry notes, IF-AE-DOCK, gen_sch_a.py's EQ-16 comment) |
| `w3de/parity/a-draft/candidate/parity_erc.json` | `128382836df9fb038a69c153ef2a20140af9af934523cf7c69d8da08462e59d2` | 5108 | `fnd/w3de` `drafts/w3de/parity/a-draft/candidate/parity_erc.json` | the w3de commit of `fnd/r8int5` (the registry notes, IF-AE-DOCK, gen_sch_a.py's EQ-16 comment) |
| `w3de/parity/a-draft/candidate/parity_intent.json` | `214d3adea5e691ba210564b1565bec561a862212c564d7b33a26efadde7d4b2c` | 79 | `fnd/w3de` `drafts/w3de/parity/a-draft/candidate/parity_intent.json` | the w3de commit of `fnd/r8int5` (the registry notes, IF-AE-DOCK, gen_sch_a.py's EQ-16 comment) |
| `w3de/parity/a-draft/candidate/parity_netlist.json` | `9ffed1141cde450ee8c0676332333e9882adead56e849bdd74d83e389e020ea2` | 6546 | `fnd/w3de` `drafts/w3de/parity/a-draft/candidate/parity_netlist.json` | the w3de commit of `fnd/r8int5` (the registry notes, IF-AE-DOCK, gen_sch_a.py's EQ-16 comment) |
| `w3de/parity/a-draft/candidate/parity_schematic.json` | `9b8dbc03adae858f245a4b441131a09cd571481ab3cf5199af5995ad921ae630` | 9122 | `fnd/w3de` `drafts/w3de/parity/a-draft/candidate/parity_schematic.json` | the w3de commit of `fnd/r8int5` (the registry notes, IF-AE-DOCK, gen_sch_a.py's EQ-16 comment) |
| `w3de/parity/a-draft/candidate/regen.json` | `e2fd8aea4a10ebb63a76f633afc4daceafb0e216e024d9634713c5d3ce0360b3` | 4558 | `fnd/w3de` `drafts/w3de/parity/a-draft/candidate/regen.json` | the w3de commit of `fnd/r8int5` (the registry notes, IF-AE-DOCK, gen_sch_a.py's EQ-16 comment) |
| `w3de/parity/a-draft/main-reproduces-main/net_compare.json` | `44f67af551fd1d05081875ec1eff462bda136b292fcb481d05fabc664de333b0` | 301 | `fnd/w3de` `drafts/w3de/parity/a-draft/main-reproduces-main/net_compare.json` | the w3de commit of `fnd/r8int5` (the registry notes, IF-AE-DOCK, gen_sch_a.py's EQ-16 comment) |
| `w3de/parity/a-draft/main-reproduces-main/parity_bom.json` | `47038bc09db73608a1a20575b23176fe777a1cf834b978d7571638a461d44571` | 68 | `fnd/w3de` `drafts/w3de/parity/a-draft/main-reproduces-main/parity_bom.json` | the w3de commit of `fnd/r8int5` (the registry notes, IF-AE-DOCK, gen_sch_a.py's EQ-16 comment) |
| `w3de/parity/a-draft/main-reproduces-main/parity_erc.json` | `efa4817108c05bf0d5d23482cd8a9adb2cd1b44255f0d09520303a3bf033c05e` | 359 | `fnd/w3de` `drafts/w3de/parity/a-draft/main-reproduces-main/parity_erc.json` | the w3de commit of `fnd/r8int5` (the registry notes, IF-AE-DOCK, gen_sch_a.py's EQ-16 comment) |
| `w3de/parity/a-draft/main-reproduces-main/parity_intent.json` | `607f2e1b7adb75dc66267217a7334114126f37ea6ca8cab0548736b90c1ba3d4` | 76 | `fnd/w3de` `drafts/w3de/parity/a-draft/main-reproduces-main/parity_intent.json` | the w3de commit of `fnd/r8int5` (the registry notes, IF-AE-DOCK, gen_sch_a.py's EQ-16 comment) |
| `w3de/parity/a-draft/main-reproduces-main/parity_netlist.json` | `9a451d517a35e0f395ad1e438ffdd7cac84eb7df495ec688ab45af3b92aea335` | 710 | `fnd/w3de` `drafts/w3de/parity/a-draft/main-reproduces-main/parity_netlist.json` | the w3de commit of `fnd/r8int5` (the registry notes, IF-AE-DOCK, gen_sch_a.py's EQ-16 comment) |
| `w3de/parity/a-draft/main-reproduces-main/parity_schematic.json` | `d5c715fceec6ddfd4b50b878ace4766442198032c47c78d4f170a18ebcb7822c` | 363 | `fnd/w3de` `drafts/w3de/parity/a-draft/main-reproduces-main/parity_schematic.json` | the w3de commit of `fnd/r8int5` (the registry notes, IF-AE-DOCK, gen_sch_a.py's EQ-16 comment) |
| `w3de/parity/a-draft/main-reproduces-main/regen.json` | `64f3238cca32799e6d0f926fefb8bc8811f2837dcd3c9c7d68d44b6a73504dea` | 4574 | `fnd/w3de` `drafts/w3de/parity/a-draft/main-reproduces-main/regen.json` | the w3de commit of `fnd/r8int5` (the registry notes, IF-AE-DOCK, gen_sch_a.py's EQ-16 comment) |
| `w3de/parity/base-main/d/parity_bom.json` | `38a45a536d61f86d91b1ac10e9c8e865434582cdf930f8240588b3f8457a9509` | 66 | `fnd/w3de` `drafts/w3de/parity/base-main/d/parity_bom.json` | the w3de commit of `fnd/r8int5` (the registry notes, IF-AE-DOCK, gen_sch_a.py's EQ-16 comment) |
| `w3de/parity/base-main/d/parity_erc.json` | `360922074f67148628c93519ed75a6c9f9690e98a268f08800c9511596d34cd6` | 353 | `fnd/w3de` `drafts/w3de/parity/base-main/d/parity_erc.json` | the w3de commit of `fnd/r8int5` (the registry notes, IF-AE-DOCK, gen_sch_a.py's EQ-16 comment) |
| `w3de/parity/base-main/d/parity_intent.json` | `607f2e1b7adb75dc66267217a7334114126f37ea6ca8cab0548736b90c1ba3d4` | 76 | `fnd/w3de` `drafts/w3de/parity/base-main/d/parity_intent.json` | the w3de commit of `fnd/r8int5` (the registry notes, IF-AE-DOCK, gen_sch_a.py's EQ-16 comment) |
| `w3de/parity/base-main/d/parity_netlist.json` | `697c6ec2bdbe686abce62aca968dbdc7e219d5008f0cb4e16b5813b5c75defb8` | 706 | `fnd/w3de` `drafts/w3de/parity/base-main/d/parity_netlist.json` | the w3de commit of `fnd/r8int5` (the registry notes, IF-AE-DOCK, gen_sch_a.py's EQ-16 comment) |
| `w3de/parity/base-main/d/parity_schematic.json` | `ace3816aae80497a8ae3464a1d9c22abfcc7bda149b6ad4942a848be40fad09d` | 361 | `fnd/w3de` `drafts/w3de/parity/base-main/d/parity_schematic.json` | the w3de commit of `fnd/r8int5` (the registry notes, IF-AE-DOCK, gen_sch_a.py's EQ-16 comment) |
| `w3de/parity/base-main/d/regen.json` | `1406894e5e2b4d3a9917048db5650743ad171ae3f100c1c0fe373a0b1e23a30f` | 5122 | `fnd/w3de` `drafts/w3de/parity/base-main/d/regen.json` | the w3de commit of `fnd/r8int5` (the registry notes, IF-AE-DOCK, gen_sch_a.py's EQ-16 comment) |
| `w3de/parity/base-main/e/parity_bom.json` | `b602b44d01c5343cb8d638927d41d50d4e1b3c801d8581142047089081324d15` | 68 | `fnd/w3de` `drafts/w3de/parity/base-main/e/parity_bom.json` | the w3de commit of `fnd/r8int5` (the registry notes, IF-AE-DOCK, gen_sch_a.py's EQ-16 comment) |
| `w3de/parity/base-main/e/parity_erc.json` | `258d1ce1835cf51e7fd9f06e28d0c7c1b3d2c0abebf0ea22770a5ac001ca6056` | 353 | `fnd/w3de` `drafts/w3de/parity/base-main/e/parity_erc.json` | the w3de commit of `fnd/r8int5` (the registry notes, IF-AE-DOCK, gen_sch_a.py's EQ-16 comment) |
| `w3de/parity/base-main/e/parity_intent.json` | `607f2e1b7adb75dc66267217a7334114126f37ea6ca8cab0548736b90c1ba3d4` | 76 | `fnd/w3de` `drafts/w3de/parity/base-main/e/parity_intent.json` | the w3de commit of `fnd/r8int5` (the registry notes, IF-AE-DOCK, gen_sch_a.py's EQ-16 comment) |
| `w3de/parity/base-main/e/parity_netlist.json` | `d435c5468f492ba064376bf9d0465556aa53f6fa18a0c58fa2bc6deaae478bd5` | 708 | `fnd/w3de` `drafts/w3de/parity/base-main/e/parity_netlist.json` | the w3de commit of `fnd/r8int5` (the registry notes, IF-AE-DOCK, gen_sch_a.py's EQ-16 comment) |
| `w3de/parity/base-main/e/parity_schematic.json` | `a5fcef76453d04e2f4b45b5d531e5756297f640a8b69ea8b2ccd7dba85bc175f` | 361 | `fnd/w3de` `drafts/w3de/parity/base-main/e/parity_schematic.json` | the w3de commit of `fnd/r8int5` (the registry notes, IF-AE-DOCK, gen_sch_a.py's EQ-16 comment) |
| `w3de/parity/base-main/e/regen.json` | `79c315c5185a7d96d4700062fba8fe400a77b2fc514ac6804370c22c98fe6da3` | 4799 | `fnd/w3de` `drafts/w3de/parity/base-main/e/regen.json` | the w3de commit of `fnd/r8int5` (the registry notes, IF-AE-DOCK, gen_sch_a.py's EQ-16 comment) |
| `w3de/parity/candidate-reproduces/d/parity_bom.json` | `38a45a536d61f86d91b1ac10e9c8e865434582cdf930f8240588b3f8457a9509` | 66 | `fnd/w3de` `drafts/w3de/parity/candidate-reproduces/d/parity_bom.json` | the w3de commit of `fnd/r8int5` (the registry notes, IF-AE-DOCK, gen_sch_a.py's EQ-16 comment) |
| `w3de/parity/candidate-reproduces/d/parity_erc.json` | `360922074f67148628c93519ed75a6c9f9690e98a268f08800c9511596d34cd6` | 353 | `fnd/w3de` `drafts/w3de/parity/candidate-reproduces/d/parity_erc.json` | the w3de commit of `fnd/r8int5` (the registry notes, IF-AE-DOCK, gen_sch_a.py's EQ-16 comment) |
| `w3de/parity/candidate-reproduces/d/parity_intent.json` | `607f2e1b7adb75dc66267217a7334114126f37ea6ca8cab0548736b90c1ba3d4` | 76 | `fnd/w3de` `drafts/w3de/parity/candidate-reproduces/d/parity_intent.json` | the w3de commit of `fnd/r8int5` (the registry notes, IF-AE-DOCK, gen_sch_a.py's EQ-16 comment) |
| `w3de/parity/candidate-reproduces/d/parity_netlist.json` | `9b894ba277bb16110ad8544f410181de440774fe3c21685ebab2d08d544c98d9` | 708 | `fnd/w3de` `drafts/w3de/parity/candidate-reproduces/d/parity_netlist.json` | the w3de commit of `fnd/r8int5` (the registry notes, IF-AE-DOCK, gen_sch_a.py's EQ-16 comment) |
| `w3de/parity/candidate-reproduces/d/parity_schematic.json` | `af98d012beb62c3341802f374720616c5c84b954b3ae08ed8dfdd133fac5dc32` | 349 | `fnd/w3de` `drafts/w3de/parity/candidate-reproduces/d/parity_schematic.json` | the w3de commit of `fnd/r8int5` (the registry notes, IF-AE-DOCK, gen_sch_a.py's EQ-16 comment) |
| `w3de/parity/candidate-reproduces/d/regen.json` | `b3d2f9d0d22ac79d97fd5f01bf0de94c1566bf0b91e0c472a4ed42efc6086fb9` | 5120 | `fnd/w3de` `drafts/w3de/parity/candidate-reproduces/d/regen.json` | the w3de commit of `fnd/r8int5` (the registry notes, IF-AE-DOCK, gen_sch_a.py's EQ-16 comment) |
| `w3de/parity/candidate-reproduces/e/parity_bom.json` | `09a7a85364829556cbc457c9d2050d8ae254742b3826ae1f6cd0e5f6843d8e9d` | 68 | `fnd/w3de` `drafts/w3de/parity/candidate-reproduces/e/parity_bom.json` | the w3de commit of `fnd/r8int5` (the registry notes, IF-AE-DOCK, gen_sch_a.py's EQ-16 comment) |
| `w3de/parity/candidate-reproduces/e/parity_erc.json` | `14039c7eaa246a5d372faaa999955a9803064d52dda9825485f196cb129abaa2` | 353 | `fnd/w3de` `drafts/w3de/parity/candidate-reproduces/e/parity_erc.json` | the w3de commit of `fnd/r8int5` (the registry notes, IF-AE-DOCK, gen_sch_a.py's EQ-16 comment) |
| `w3de/parity/candidate-reproduces/e/parity_intent.json` | `607f2e1b7adb75dc66267217a7334114126f37ea6ca8cab0548736b90c1ba3d4` | 76 | `fnd/w3de` `drafts/w3de/parity/candidate-reproduces/e/parity_intent.json` | the w3de commit of `fnd/r8int5` (the registry notes, IF-AE-DOCK, gen_sch_a.py's EQ-16 comment) |
| `w3de/parity/candidate-reproduces/e/parity_netlist.json` | `09a7f6744b06d73ee3a3236b147c8f4225730ace889e2df10aa52be6f21a2b55` | 712 | `fnd/w3de` `drafts/w3de/parity/candidate-reproduces/e/parity_netlist.json` | the w3de commit of `fnd/r8int5` (the registry notes, IF-AE-DOCK, gen_sch_a.py's EQ-16 comment) |
| `w3de/parity/candidate-reproduces/e/parity_schematic.json` | `ace929ea68219b80b5988bb0d9b42f9a99b6fdda1b7305c112faa594f6a07d7d` | 349 | `fnd/w3de` `drafts/w3de/parity/candidate-reproduces/e/parity_schematic.json` | the w3de commit of `fnd/r8int5` (the registry notes, IF-AE-DOCK, gen_sch_a.py's EQ-16 comment) |
| `w3de/parity/candidate-reproduces/e/regen.json` | `a1bbd855db342fc6a89369ec2276f2df0e2e42ad5cdd2da0a0df92633e17660f` | 4795 | `fnd/w3de` `drafts/w3de/parity/candidate-reproduces/e/regen.json` | the w3de commit of `fnd/r8int5` (the registry notes, IF-AE-DOCK, gen_sch_a.py's EQ-16 comment) |
| `w3de/parity/candidate/d/parity_bom.json` | `38a45a536d61f86d91b1ac10e9c8e865434582cdf930f8240588b3f8457a9509` | 66 | `fnd/w3de` `drafts/w3de/parity/candidate/d/parity_bom.json` | the w3de commit of `fnd/r8int5` (the registry notes, IF-AE-DOCK, gen_sch_a.py's EQ-16 comment) |
| `w3de/parity/candidate/d/parity_erc.json` | `360922074f67148628c93519ed75a6c9f9690e98a268f08800c9511596d34cd6` | 353 | `fnd/w3de` `drafts/w3de/parity/candidate/d/parity_erc.json` | the w3de commit of `fnd/r8int5` (the registry notes, IF-AE-DOCK, gen_sch_a.py's EQ-16 comment) |
| `w3de/parity/candidate/d/parity_intent.json` | `0ab2ee8a0ee82520c1aba8c09466bea8528f114015ec151d6b2dcaf83ad476cb` | 79 | `fnd/w3de` `drafts/w3de/parity/candidate/d/parity_intent.json` | the w3de commit of `fnd/r8int5` (the registry notes, IF-AE-DOCK, gen_sch_a.py's EQ-16 comment) |
| `w3de/parity/candidate/d/parity_netlist.json` | `a5fd689532976ca043c18da28b9767b0627d17831eb2b175710387524abb0064` | 707 | `fnd/w3de` `drafts/w3de/parity/candidate/d/parity_netlist.json` | the w3de commit of `fnd/r8int5` (the registry notes, IF-AE-DOCK, gen_sch_a.py's EQ-16 comment) |
| `w3de/parity/candidate/d/parity_schematic.json` | `ace3816aae80497a8ae3464a1d9c22abfcc7bda149b6ad4942a848be40fad09d` | 361 | `fnd/w3de` `drafts/w3de/parity/candidate/d/parity_schematic.json` | the w3de commit of `fnd/r8int5` (the registry notes, IF-AE-DOCK, gen_sch_a.py's EQ-16 comment) |
| `w3de/parity/candidate/d/regen.json` | `a89b27872e0e2abe9683927d9caf981ba171c74bbc785d799a06b83fcaa49dfa` | 5136 | `fnd/w3de` `drafts/w3de/parity/candidate/d/regen.json` | the w3de commit of `fnd/r8int5` (the registry notes, IF-AE-DOCK, gen_sch_a.py's EQ-16 comment) |
| `w3de/parity/candidate/e/parity_bom.json` | `ace0a54913238aff4d05e23a0d1283cb7708a19f9f2428e3af3255598bc5a740` | 1415 | `fnd/w3de` `drafts/w3de/parity/candidate/e/parity_bom.json` | the w3de commit of `fnd/r8int5` (the registry notes, IF-AE-DOCK, gen_sch_a.py's EQ-16 comment) |
| `w3de/parity/candidate/e/parity_erc.json` | `68635e38ea32c1fddce23d9c8724ecd6f359c75524571eed8c63783a4ba363ea` | 1362 | `fnd/w3de` `drafts/w3de/parity/candidate/e/parity_erc.json` | the w3de commit of `fnd/r8int5` (the registry notes, IF-AE-DOCK, gen_sch_a.py's EQ-16 comment) |
| `w3de/parity/candidate/e/parity_intent.json` | `3831d89bf7be4ac251a41557a004af5fc975d91961875df923bfaa1d41b2ab12` | 102 | `fnd/w3de` `drafts/w3de/parity/candidate/e/parity_intent.json` | the w3de commit of `fnd/r8int5` (the registry notes, IF-AE-DOCK, gen_sch_a.py's EQ-16 comment) |
| `w3de/parity/candidate/e/parity_netlist.json` | `53f3c0040b317dc3a43f13672dd189fbd197773b496362db8fc02025fbfbc58d` | 7265 | `fnd/w3de` `drafts/w3de/parity/candidate/e/parity_netlist.json` | the w3de commit of `fnd/r8int5` (the registry notes, IF-AE-DOCK, gen_sch_a.py's EQ-16 comment) |
| `w3de/parity/candidate/e/parity_schematic.json` | `9db67adf5a56a01c1b7cae13b879b6eb0be216a6bc3bf7381d0b460dbea21fac` | 10420 | `fnd/w3de` `drafts/w3de/parity/candidate/e/parity_schematic.json` | the w3de commit of `fnd/r8int5` (the registry notes, IF-AE-DOCK, gen_sch_a.py's EQ-16 comment) |
| `w3de/parity/candidate/e/regen.json` | `f59d4441b28f4a0710d8c5fcf57416fe076817f4087a8c680fb2952bba79d404` | 4787 | `fnd/w3de` `drafts/w3de/parity/candidate/e/regen.json` | the w3de commit of `fnd/r8int5` (the registry notes, IF-AE-DOCK, gen_sch_a.py's EQ-16 comment) |
| `w3de/parity/expected-a-netlist.json` | `69826c246fafacc5b5fe0b619f8a0dfabed3de01ce254e97ba19ac8cd52103a9` | 567 | `fnd/w3de` `drafts/w3de/parity/expected-a-netlist.json` | the w3de commit of `fnd/r8int5` (the registry notes, IF-AE-DOCK, gen_sch_a.py's EQ-16 comment) |
| `w3de/parity/expected-d-netlist.json` | `922903ce2253dc6c53ad9d4a415c93a98b3cc37077a48a565546e6ad78dfae83` | 171 | `fnd/w3de` `drafts/w3de/parity/expected-d-netlist.json` | the w3de commit of `fnd/r8int5` (the registry notes, IF-AE-DOCK, gen_sch_a.py's EQ-16 comment) |
| `w3de/parity/expected-e-netlist.json` | `ec74290e6576ec6f12c39bd8a552f58128c51e3248a808bce934efc8e3dc3c35` | 922 | `fnd/w3de` `drafts/w3de/parity/expected-e-netlist.json` | the w3de commit of `fnd/r8int5` (the registry notes, IF-AE-DOCK, gen_sch_a.py's EQ-16 comment) |
| `w3de/patch_assembly_dock.py` | `ea6aea2424b559b0434deedc45f98a7abfd29b9a49e9840bff69a550ca0fda61` | 2736 | `fnd/w3de` `drafts/w3de/patch_assembly_dock.py` | the w3de commit of `fnd/r8int5` (the registry notes, IF-AE-DOCK, gen_sch_a.py's EQ-16 comment) |
| `w3de/patch_check_contracts_dock.py` | `2002fbe809d771e1f545795064ac571eb8eb6dbd442f027f8e961e8664b575e1` | 2987 | `fnd/w3de` `drafts/w3de/patch_check_contracts_dock.py` | the w3de commit of `fnd/r8int5` (the registry notes, IF-AE-DOCK, gen_sch_a.py's EQ-16 comment) |
| `w3de/patch_energy_chain.py` | `9d84b62047d7af72bae4d2745b433765178985c17929271df5f94abd2cdf0f22` | 10398 | `fnd/w3de` `drafts/w3de/patch_energy_chain.py` | the w3de commit of `fnd/r8int5` (the registry notes, IF-AE-DOCK, gen_sch_a.py's EQ-16 comment) |
| `w3de/patch_gen_pcb_e3.py` | `74ba95548e60e39f65ff36f54f64858629d0ed68b1921655932e5181eac0ed84` | 2747 | `fnd/w3de` `drafts/w3de/patch_gen_pcb_e3.py` | the w3de commit of `fnd/r8int5` (the registry notes, IF-AE-DOCK, gen_sch_a.py's EQ-16 comment) |
| `w3de/patch_gen_sch_a_dock.py` | `404c5e64ebeab9522930cce78e04f83cbb7d7c7c8b9a62e60d23714801583d44` | 7091 | `fnd/w3de` `drafts/w3de/patch_gen_sch_a_dock.py` | the w3de commit of `fnd/r8int5` (the registry notes, IF-AE-DOCK, gen_sch_a.py's EQ-16 comment) |
| `w3de/patch_gen_sch_a_dock_r8int5.py` | `bee758bcf23ec3b9944d44356a2979270e7ebca4b29a5602a520badc0eb30b1b` | 3115 | the r8int5 integrator (`patch_gen_sch_a_dock_r8int5.py`) | the w3de commit of `fnd/r8int5` (the registry notes, IF-AE-DOCK, gen_sch_a.py's EQ-16 comment) |
| `w3de/patch_interfaces_if_ae_dock.py` | `9951cdf3efa25e2b3a4dd5c48d0dff4de49000bdfbce295237c12a561286cc3a` | 8276 | `fnd/w3de` `drafts/w3de/patch_interfaces_if_ae_dock.py` | the w3de commit of `fnd/r8int5` (the registry notes, IF-AE-DOCK, gen_sch_a.py's EQ-16 comment) |
| `w3de/patch_interfaces_r8int5.py` | `d3bf07d7059014cccf6dca10e8fa7fa60c432b213eedb80eccda99e52df209de` | 4631 | the r8int5 integrator (`patch_interfaces_r8int5.py`) | the w3de commit of `fnd/r8int5` (the registry notes, IF-AE-DOCK, gen_sch_a.py's EQ-16 comment) |
| `w3de/patch_pcb_sensitive_e.py` | `d5e4173ca84eeddd6263cc64285c5d24996a6ce0c24219a5a29ad3f74c092255` | 5789 | `fnd/w3de` `drafts/w3de/patch_pcb_sensitive_e.py` | the w3de commit of `fnd/r8int5` (the registry notes, IF-AE-DOCK, gen_sch_a.py's EQ-16 comment) |
| `w3de/patch_test_rails_census.py` | `de8700edf5132651a597b5c9339809be18bea287c49bae821c2d49e2b07b8aa4` | 2290 | `fnd/w3de` `drafts/w3de/patch_test_rails_census.py` | the w3de commit of `fnd/r8int5` (the registry notes, IF-AE-DOCK, gen_sch_a.py's EQ-16 comment) |
| `w3de/run_gates.sh` | `4300260e3bccb7ecfcd8fb164fc50d1e6e8755c3d3b76e93581a850a47016b1c` | 2929 | `fnd/w3de` `drafts/w3de/run_gates.sh` | the w3de commit of `fnd/r8int5` (the registry notes, IF-AE-DOCK, gen_sch_a.py's EQ-16 comment) |
| `w3g/README.md` | `9a749d5b5bf8aff5bf056a418b72a6b6c61d1e67d890558855530c5fcff2ecf3` | 1098 | `fnd/w3g` `drafts/w3g/README.md` | the w3g commit of `fnd/r8int5` (v2/docs/diagrams/, ARCHITECTURE.md's reference lines) |
| `w3g/apply_handover_labels.py` | `835445bd71b80ae9b77c2eafa26080dfe8be58b00d9f62f08d02ac90a23a7b35` | 3584 | `fnd/w3g` `drafts/w3g/apply_handover_labels.py` | the w3g commit of `fnd/r8int5` (v2/docs/diagrams/, ARCHITECTURE.md's reference lines) |
| `w3g/architecture-w3g.diff` | `8522d770edc354ad6c9c448614260c920664e30d6e48a1f294a01dd0c9b64079` | 8746 | the r8int5 integrator (`architecture-w3g.diff`) | the w3g commit of `fnd/r8int5` (v2/docs/diagrams/, ARCHITECTURE.md's reference lines) |
| `w3g/architecture_counts_r8int5.py` | `b328e7b19e5a8f414d99ccf60b1de531fd1710cd96a52827e1840a9512139cd2` | 2324 | the r8int5 integrator (`architecture_counts_r8int5.py`) | the w3g commit of `fnd/r8int5` (v2/docs/diagrams/, ARCHITECTURE.md's reference lines) |
| `w3g/architecture_refs_r8int5.py` | `18a7bf4fb3c18d1107b3f26184812796f6b3d360ba4c0960eb4e826f1b287576` | 1711 | the r8int5 integrator (`architecture_refs_r8int5.py`) | the w3g commit of `fnd/r8int5` (v2/docs/diagrams/, ARCHITECTURE.md's reference lines) |
| `w3g/files.lst` | `73eb1b51b01421156a2451ed0ada1b4b9ec4f85ad0a7128665648a702e4ad3bd` | 1762 | the r8int5 integrator (`files.lst`) | the w3g commit of `fnd/r8int5` (v2/docs/diagrams/, ARCHITECTURE.md's reference lines) |
| `w3g/finding-pcb-e-fet-symbol.md` | `cf538d95ceb5363113bdb03c22da8f218ef4bdbec6b5aa0861276fda284a00a7` | 2355 | `fnd/w3g` `drafts/w3g/finding-pcb-e-fet-symbol.md` | the w3g commit of `fnd/r8int5` (v2/docs/diagrams/, ARCHITECTURE.md's reference lines) |
| `w3g/power_tree_r8int5.py` | `86dedd4bed6ba04e61424b95cf29b32ea9709534e1f772e86655cfed2d65791e` | 2480 | the r8int5 integrator (`power_tree_r8int5.py`) | the w3g commit of `fnd/r8int5` (v2/docs/diagrams/, ARCHITECTURE.md's reference lines) |
| `w3g/readme_r8int5.py` | `22c3cced77289393d6c5b8a0d097d29053618fc6c134edd9c95d1c065c419064` | 6572 | the r8int5 integrator (`readme_r8int5.py`) | the w3g commit of `fnd/r8int5` (v2/docs/diagrams/, ARCHITECTURE.md's reference lines) |
| `w3t/HANDOFF.md` | `c5f06cc02981bbcfc40bf0bf8448b3346070485d6ef122bc5269191a090538fa` | 5878 | `fnd/w3t` `drafts/w3t/HANDOFF.md` | v2/ecad/tools/pcb_requirements.yaml (S-64)<br>v2/docs/handover/ENGINEERING-QUESTIONS.md (EQ-25) |
| `w3t/apply_registry.py` | `649dfa5f83719566360047592f6957d52aa720b4121a8869e273eaf34c8d7a02` | 13863 | `fnd/w3t` `drafts/w3t/apply_registry.py` | the r8int5 integration (it applied RF-002's coverage row and S-64) |
| `w3t/readings/inhibit-chain-before-after.txt` | `5f9acd1b9d969a3105618f36c58f009aa623e9fe77836327a27b2a429e91ac3b` | 1113 | `fnd/w3t` `drafts/w3t/readings/inhibit-chain-before-after.txt` | v2/docs/handover/ENGINEERING-QUESTIONS.md (EQ-25) |
| `w3t/readings/walk-after-w3t.json` | `f3376a666688f87c7ad5dffd656b255d0fd4b49e58475682f01c01ad5f27ce03` | 20131 | `fnd/w3t` `drafts/w3t/readings/walk-after-w3t.json` | w3t-decisions.md section 4 |
| `w3t/readings/walk-before-main-38dcd764.json` | `34130f160f66f1b57c7f1c6494ea9aaa6081a7314df81e08a2861af50b2f3a8d` | 21077 | `fnd/w3t` `drafts/w3t/readings/walk-before-main-38dcd764.json` | w3t-decisions.md section 4 |
| `w3t/w3t-decisions.md` | `d9d695e4a0f5c19426d7f9625b634fb0ba7dcc5cea5c209e0ce0bbb06e6a907f` | 12585 | `fnd/w3t` `drafts/w3t/w3t-decisions.md` | v2/ecad/tools/pcb_requirements.yaml (S-64)<br>v2/docs/handover/ENGINEERING-QUESTIONS.md (EQ-18, EQ-25)<br>v2/docs/feasibility/EMCON.md (section 4b) |
| `w4/w4-mech-thermal-rf.md` | `ba590c405b672995eee2094ec302eb08ddfed9ca49a7411d71041ffd459bd42e` | 52637 | `fnd/w4` `drafts/w4-mech-thermal-rf.md` | `v2/docs/feasibility/POWER-THERMAL.md` |
| `w4/w4-scratch-thermal.py` | `6c83da5f7e3e4f0f5393bfe0f609ba02c423adbadfa3661a245d0a9b778e65c3` | 9871 | `fnd/w4` `drafts/w4-scratch-thermal.py` | `v2/docs/feasibility/POWER-THERMAL.md` |
| `w4ae/README.md` | `1aca4c55a9e8e0e0932fe0f0aadd0cc0ce834f7feac9069d3c39beb2f69920db` | 9709 | `fnd/w4ae` `drafts/w4ae/README.md` | the w4ae commit; REQ-077's desk reading; the registry's HOT-R1 and fan-node choices; EQ-22 |
| `w4ae/apply_registry.py` | `1f653f3f6252109871515bc96177ea99e4cbc9378711fb7b623c37c569659d49` | 22078 | `fnd/w4ae` `drafts/w4ae/apply_registry.py` | the w4ae commit; REQ-077's desk reading; the registry's HOT-R1 and fan-node choices; EQ-22 |
| `w4ae/apply_registry_r8int6.py` | `17ef8199c0a6b03f886ec0894df3a9dd7094910b385b1984341f2d12055aeba0` | 23022 | the r8int6 integrator (`apply_registry_r8int6.py`) | the w4ae commit; REQ-077's desk reading; the registry's HOT-R1 and fan-node choices; EQ-22 |
| `w4ae/apply_w4ae_r8int6.sh` | `7caf8c1a6b6e0035890d44dc619558bbef07b0a7c35b6ef915447716ebe0877a` | 1843 | the r8int6 integrator (`apply_w4ae_r8int6.sh`) | the w4ae commit; REQ-077's desk reading; the registry's HOT-R1 and fan-node choices; EQ-22 |
| `w4ae/derive_w4ae_r8int6.py` | `0365339023780f58b75674da815166bc9188fb0f914a48fb477eb657407c8e7b` | 6365 | the r8int6 integrator (`derive_w4ae_r8int6.py`) | the w4ae commit; REQ-077's desk reading; the registry's HOT-R1 and fan-node choices; EQ-22 |
| `w4ae/edit_docs.py` | `1da308d621a50dc5f5c18be77facf274df9a4540b9cf5e4c941ab0be9d94f55e` | 21122 | `fnd/w4ae` `drafts/w4ae/edit_docs.py` | the w4ae commit; REQ-077's desk reading; the registry's HOT-R1 and fan-node choices; EQ-22 |
| `w4ae/edit_docs_r8int6.py` | `bbc15694ee86f32cfc86293d498604fc304c3e1cc2c3a67cefa6a016da7a5903` | 21858 | the r8int6 integrator (`edit_docs_r8int6.py`) | the w4ae commit; REQ-077's desk reading; the registry's HOT-R1 and fan-node choices; EQ-22 |
| `w4ae/fixes_w4ae_r8int6.py` | `d82e46d1df2eb471f9eca3cf5d7bc59555bd6759deab932d5fe1b8a567c02a09` | 3398 | the r8int6 integrator (`fixes_w4ae_r8int6.py`) | the w4ae commit; REQ-077's desk reading; the registry's HOT-R1 and fan-node choices; EQ-22 |
| `w4ae/hot_r1_trace.py` | `2350c321fa7442934b21bfc59d2ad44ef600cecc031f7244c6a78269c2bc3dc0` | 13829 | `fnd/w4ae` `drafts/w4ae/hot_r1_trace.py` | the w4ae commit; REQ-077's desk reading; the registry's HOT-R1 and fan-node choices; EQ-22 |
| `w4ae/ids.json` | `1f06cf8cef8ca3f35d843e15892b033701b088b3616cb5beb28638978ce1f54d` | 46 | `fnd/w4ae` `drafts/w4ae/ids.json` | the w4ae commit; REQ-077's desk reading; the registry's HOT-R1 and fan-node choices; EQ-22 |
| `w4ae/ids_r8int6.json` | `d6ee894eecdc2a5dffd033cb947e8b3642d517b16920967194924e6792a7fe6f` | 67 | the r8int6 integrator (`ids_r8int6.json`) | the w4ae commit; REQ-077's desk reading; the registry's HOT-R1 and fan-node choices; EQ-22 |
| `w4ae/integrate.sh` | `032a94775ac29ae97ca3db55f47683b86585a76cc1f75046c1e2282360b36068` | 2354 | `fnd/w4ae` `drafts/w4ae/integrate.sh` | the w4ae commit; REQ-077's desk reading; the registry's HOT-R1 and fan-node choices; EQ-22 |
| `w4ae/jlc/lcsc-api-C133091.json` | `1d6de451d3caf74407d1670b5bbbb087fe2b2d5c1229d9517b71ae372a036bf9` | 38227 | `fnd/w4ae` `drafts/w4ae/jlc/lcsc-api-C133091.json` | the w4ae commit; REQ-077's desk reading; the registry's HOT-R1 and fan-node choices; EQ-22 |
| `w4ae/jlc/lcsc-api-C51897884.json` | `a86e135fd9e76049a75c577cf98b0b67134bf05ac5638e61ac1583ded0e2f901` | 47 | `fnd/w4ae` `drafts/w4ae/jlc/lcsc-api-C51897884.json` | the w4ae commit; REQ-077's desk reading; the registry's HOT-R1 and fan-node choices; EQ-22 |
| `w4ae/jlc/q-MBRS140T3G.json` | `93f1b301461dfdb913e14500e61f95c08b1cae069c9a0b5d344b9b20f001d71f` | 22255 | `fnd/w4ae` `drafts/w4ae/jlc/q-MBRS140T3G.json` | the w4ae commit; REQ-077's desk reading; the registry's HOT-R1 and fan-node choices; EQ-22 |
| `w4ae/jlc/q-SS14_SMB.json` | `2fddd0af0cee3cf1cbe31cd72a276b884d6910a18dd4b899e733b95446f1a62c` | 12364 | `fnd/w4ae` `drafts/w4ae/jlc/q-SS14_SMB.json` | the w4ae commit; REQ-077's desk reading; the registry's HOT-R1 and fan-node choices; EQ-22 |
| `w4ae/parity/candidate-reproduces/a/net_compare.txt` | `fd4c748638ff2dc2c2ac236c9d098b0483f5a91545cd7109461d9de597b91463` | 210 | `fnd/w4ae` `drafts/w4ae/parity/candidate-reproduces/a/net_compare.txt` | the w4ae commit; REQ-077's desk reading; the registry's HOT-R1 and fan-node choices; EQ-22 |
| `w4ae/parity/candidate-reproduces/a/parity_bom.json` | `5145580aba2011e2b5f33bb043e39677356bff43fef0c69f62fa928d20950422` | 68 | `fnd/w4ae` `drafts/w4ae/parity/candidate-reproduces/a/parity_bom.json` | the w4ae commit; REQ-077's desk reading; the registry's HOT-R1 and fan-node choices; EQ-22 |
| `w4ae/parity/candidate-reproduces/a/parity_erc.json` | `0a2c44151af1c9dad222305680437412aee13d7633ab473c877079ffc1fe8298` | 359 | `fnd/w4ae` `drafts/w4ae/parity/candidate-reproduces/a/parity_erc.json` | the w4ae commit; REQ-077's desk reading; the registry's HOT-R1 and fan-node choices; EQ-22 |
| `w4ae/parity/candidate-reproduces/a/parity_intent.json` | `9a6cca7444ba1af0225fb9762f0be3a637ad9c120d10781d698f9e7d5aa390ea` | 43 | `fnd/w4ae` `drafts/w4ae/parity/candidate-reproduces/a/parity_intent.json` | the w4ae commit; REQ-077's desk reading; the registry's HOT-R1 and fan-node choices; EQ-22 |
| `w4ae/parity/candidate-reproduces/a/parity_netlist.json` | `088f23b324a8dbad4353224ff27a377e9da986950244554c0994fe3ee9e56e7f` | 710 | `fnd/w4ae` `drafts/w4ae/parity/candidate-reproduces/a/parity_netlist.json` | the w4ae commit; REQ-077's desk reading; the registry's HOT-R1 and fan-node choices; EQ-22 |
| `w4ae/parity/candidate-reproduces/a/parity_schematic.json` | `785d0297dafc79b7c6f22f72f9b4f0106e23bd314dce674116c445fcafa4fe70` | 351 | `fnd/w4ae` `drafts/w4ae/parity/candidate-reproduces/a/parity_schematic.json` | the w4ae commit; REQ-077's desk reading; the registry's HOT-R1 and fan-node choices; EQ-22 |
| `w4ae/parity/candidate-reproduces/a/regen.json` | `a5072ee9d4328432bed203d71eb98af40c653784298dc2f5b640020abe03a047` | 4575 | `fnd/w4ae` `drafts/w4ae/parity/candidate-reproduces/a/regen.json` | the w4ae commit; REQ-077's desk reading; the registry's HOT-R1 and fan-node choices; EQ-22 |
| `w4ae/parity/candidate-reproduces/e/net_compare.txt` | `edf26f2b2680d63928560c340482e82e42c005b511c4a7f0b84475dfdb5a57d2` | 208 | `fnd/w4ae` `drafts/w4ae/parity/candidate-reproduces/e/net_compare.txt` | the w4ae commit; REQ-077's desk reading; the registry's HOT-R1 and fan-node choices; EQ-22 |
| `w4ae/parity/candidate-reproduces/e/parity_bom.json` | `4b3097655bf663177985428b8fda28e7e48409cdbadcab72076fc20db05cccf2` | 68 | `fnd/w4ae` `drafts/w4ae/parity/candidate-reproduces/e/parity_bom.json` | the w4ae commit; REQ-077's desk reading; the registry's HOT-R1 and fan-node choices; EQ-22 |
| `w4ae/parity/candidate-reproduces/e/parity_erc.json` | `b6c52f4aaefee78154b5d74e1675408cef8fe524fb25171cfa4bce9dcc659b7a` | 353 | `fnd/w4ae` `drafts/w4ae/parity/candidate-reproduces/e/parity_erc.json` | the w4ae commit; REQ-077's desk reading; the registry's HOT-R1 and fan-node choices; EQ-22 |
| `w4ae/parity/candidate-reproduces/e/parity_intent.json` | `607f2e1b7adb75dc66267217a7334114126f37ea6ca8cab0548736b90c1ba3d4` | 76 | `fnd/w4ae` `drafts/w4ae/parity/candidate-reproduces/e/parity_intent.json` | the w4ae commit; REQ-077's desk reading; the registry's HOT-R1 and fan-node choices; EQ-22 |
| `w4ae/parity/candidate-reproduces/e/parity_netlist.json` | `f4a2458329adb41d7c4a2d066f24e9f0345d14329e739f123f49515a8f3b2387` | 710 | `fnd/w4ae` `drafts/w4ae/parity/candidate-reproduces/e/parity_netlist.json` | the w4ae commit; REQ-077's desk reading; the registry's HOT-R1 and fan-node choices; EQ-22 |
| `w4ae/parity/candidate-reproduces/e/parity_schematic.json` | `ace929ea68219b80b5988bb0d9b42f9a99b6fdda1b7305c112faa594f6a07d7d` | 349 | `fnd/w4ae` `drafts/w4ae/parity/candidate-reproduces/e/parity_schematic.json` | the w4ae commit; REQ-077's desk reading; the registry's HOT-R1 and fan-node choices; EQ-22 |
| `w4ae/parity/candidate-reproduces/e/regen.json` | `b05ff809699130f45959a284716dda0fc7197d4db4c862497280406ce90d57ec` | 4803 | `fnd/w4ae` `drafts/w4ae/parity/candidate-reproduces/e/regen.json` | the w4ae commit; REQ-077's desk reading; the registry's HOT-R1 and fan-node choices; EQ-22 |
| `w4ae/parity/candidate/a/intent_compare.txt` | `e3b0c44298fc1c149afbf4c8996fb92427ae41e4649b934ca495991b7852b855` | 0 | `fnd/w4ae` `drafts/w4ae/parity/candidate/a/intent_compare.txt` | the w4ae commit; REQ-077's desk reading; the registry's HOT-R1 and fan-node choices; EQ-22 |
| `w4ae/parity/candidate/a/net_compare.txt` | `1f83168af579a880730aba67e325773f304897f02d0ee0b3956c3ca1c2bf6313` | 767 | `fnd/w4ae` `drafts/w4ae/parity/candidate/a/net_compare.txt` | the w4ae commit; REQ-077's desk reading; the registry's HOT-R1 and fan-node choices; EQ-22 |
| `w4ae/parity/candidate/a/parity_bom.json` | `e0b45157c0d0a25f46e30c6f5b1bee9ddc4e777835de86c54f7882760ed149a8` | 997 | `fnd/w4ae` `drafts/w4ae/parity/candidate/a/parity_bom.json` | the w4ae commit; REQ-077's desk reading; the registry's HOT-R1 and fan-node choices; EQ-22 |
| `w4ae/parity/candidate/a/parity_erc.json` | `9fef1e7c897a2ead05871ad4d3e1b2f4390eff42d31338bda98674ce9b33a0ca` | 4241 | `fnd/w4ae` `drafts/w4ae/parity/candidate/a/parity_erc.json` | the w4ae commit; REQ-077's desk reading; the registry's HOT-R1 and fan-node choices; EQ-22 |
| `w4ae/parity/candidate/a/parity_intent.json` | `607f2e1b7adb75dc66267217a7334114126f37ea6ca8cab0548736b90c1ba3d4` | 76 | `fnd/w4ae` `drafts/w4ae/parity/candidate/a/parity_intent.json` | the w4ae commit; REQ-077's desk reading; the registry's HOT-R1 and fan-node choices; EQ-22 |
| `w4ae/parity/candidate/a/parity_netlist.json` | `9bc954d3fead864682206569b1904a196837c127150deb73f9cfe9cdc3acf466` | 5593 | `fnd/w4ae` `drafts/w4ae/parity/candidate/a/parity_netlist.json` | the w4ae commit; REQ-077's desk reading; the registry's HOT-R1 and fan-node choices; EQ-22 |
| `w4ae/parity/candidate/a/parity_schematic.json` | `6a14974c54c5665a9a09522c3ecb766f0788919113ef1ba96e7ebff0d0892ee1` | 8339 | `fnd/w4ae` `drafts/w4ae/parity/candidate/a/parity_schematic.json` | the w4ae commit; REQ-077's desk reading; the registry's HOT-R1 and fan-node choices; EQ-22 |
| `w4ae/parity/candidate/a/regen.json` | `47ba9aedeaffc7cd6d3854aa25d8882b8264837277bf2afd82fbc4602a1b9151` | 4568 | `fnd/w4ae` `drafts/w4ae/parity/candidate/a/regen.json` | the w4ae commit; REQ-077's desk reading; the registry's HOT-R1 and fan-node choices; EQ-22 |
| `w4ae/parity/candidate/e/intent_compare.txt` | `9cee5eaa074893487c72d33a1fe1c1dc29c90703cc3ec674bc9d456fd5a26a24` | 42 | `fnd/w4ae` `drafts/w4ae/parity/candidate/e/intent_compare.txt` | the w4ae commit; REQ-077's desk reading; the registry's HOT-R1 and fan-node choices; EQ-22 |
| `w4ae/parity/candidate/e/net_compare.txt` | `6716a9a99c597a50c4bf82ae554d91de72bf60aab54db89c273712cb409604ee` | 1073 | `fnd/w4ae` `drafts/w4ae/parity/candidate/e/net_compare.txt` | the w4ae commit; REQ-077's desk reading; the registry's HOT-R1 and fan-node choices; EQ-22 |
| `w4ae/parity/candidate/e/parity_bom.json` | `dbd2140e3ed9754f24b0566448d7b119eae2e52af01575e7877b334d3eaf7229` | 1420 | `fnd/w4ae` `drafts/w4ae/parity/candidate/e/parity_bom.json` | the w4ae commit; REQ-077's desk reading; the registry's HOT-R1 and fan-node choices; EQ-22 |
| `w4ae/parity/candidate/e/parity_erc.json` | `40dcada2f1c8184494974600568d68e3bff9c66a97e5a41eec4224e402c3789d` | 2358 | `fnd/w4ae` `drafts/w4ae/parity/candidate/e/parity_erc.json` | the w4ae commit; REQ-077's desk reading; the registry's HOT-R1 and fan-node choices; EQ-22 |
| `w4ae/parity/candidate/e/parity_intent.json` | `0ab2ee8a0ee82520c1aba8c09466bea8528f114015ec151d6b2dcaf83ad476cb` | 79 | `fnd/w4ae` `drafts/w4ae/parity/candidate/e/parity_intent.json` | the w4ae commit; REQ-077's desk reading; the registry's HOT-R1 and fan-node choices; EQ-22 |
| `w4ae/parity/candidate/e/parity_netlist.json` | `2ef97b9328319d07786e21b3594c4aa7bf0b9bd54950a3136fac01f90cd97891` | 6831 | `fnd/w4ae` `drafts/w4ae/parity/candidate/e/parity_netlist.json` | the w4ae commit; REQ-077's desk reading; the registry's HOT-R1 and fan-node choices; EQ-22 |
| `w4ae/parity/candidate/e/parity_schematic.json` | `5a524648b4e6977ab669594c21c9774ee2ed407b8d5a6d872569ab88324876ee` | 3880 | `fnd/w4ae` `drafts/w4ae/parity/candidate/e/parity_schematic.json` | the w4ae commit; REQ-077's desk reading; the registry's HOT-R1 and fan-node choices; EQ-22 |
| `w4ae/parity/candidate/e/regen.json` | `4af9dee5af02b23589564f41c58109b692e23b8ebebe7b1653f667ceefc31e70` | 4775 | `fnd/w4ae` `drafts/w4ae/parity/candidate/e/regen.json` | the w4ae commit; REQ-077's desk reading; the registry's HOT-R1 and fan-node choices; EQ-22 |
| `w4ae/parity/expected-a-netlist.json` | `7572ea07813232cb8422fe4fdc839a95f4603025b51fd06e4af7aa2307f50cff` | 243 | `fnd/w4ae` `drafts/w4ae/parity/expected-a-netlist.json` | the w4ae commit; REQ-077's desk reading; the registry's HOT-R1 and fan-node choices; EQ-22 |
| `w4ae/parity/expected-e-netlist.json` | `2c92d4091bec36e2abb8171501cf4cc4161526ecd68133d72b896560840dd220` | 470 | `fnd/w4ae` `drafts/w4ae/parity/expected-e-netlist.json` | the w4ae commit; REQ-077's desk reading; the registry's HOT-R1 and fan-node choices; EQ-22 |
| `w4ae/parity/expected-none.json` | `ca3d163bab055381827226140568f3bef7eaac187cebd76878e0b63e9e442356` | 3 | `fnd/w4ae` `drafts/w4ae/parity/expected-none.json` | the w4ae commit; REQ-077's desk reading; the registry's HOT-R1 and fan-node choices; EQ-22 |
| `w4ae/parity/main-reproduces-main/a/net_compare.txt` | `24a2c4067ba0e9e103c81bd0c10114fa5e3208e94460c909e0e14bdf417e4dae` | 210 | `fnd/w4ae` `drafts/w4ae/parity/main-reproduces-main/a/net_compare.txt` | the w4ae commit; REQ-077's desk reading; the registry's HOT-R1 and fan-node choices; EQ-22 |
| `w4ae/parity/main-reproduces-main/a/parity_bom.json` | `5145580aba2011e2b5f33bb043e39677356bff43fef0c69f62fa928d20950422` | 68 | `fnd/w4ae` `drafts/w4ae/parity/main-reproduces-main/a/parity_bom.json` | the w4ae commit; REQ-077's desk reading; the registry's HOT-R1 and fan-node choices; EQ-22 |
| `w4ae/parity/main-reproduces-main/a/parity_erc.json` | `75c8d22743f41d58885766af21fd940066b6cbb6132b7cd939e3314ec5d8b5c6` | 359 | `fnd/w4ae` `drafts/w4ae/parity/main-reproduces-main/a/parity_erc.json` | the w4ae commit; REQ-077's desk reading; the registry's HOT-R1 and fan-node choices; EQ-22 |
| `w4ae/parity/main-reproduces-main/a/parity_intent.json` | `607f2e1b7adb75dc66267217a7334114126f37ea6ca8cab0548736b90c1ba3d4` | 76 | `fnd/w4ae` `drafts/w4ae/parity/main-reproduces-main/a/parity_intent.json` | the w4ae commit; REQ-077's desk reading; the registry's HOT-R1 and fan-node choices; EQ-22 |
| `w4ae/parity/main-reproduces-main/a/parity_netlist.json` | `216adb5c8a60cece6de67a7458180ed4b6140774c4f52c06ad2a60d5ee598fe0` | 710 | `fnd/w4ae` `drafts/w4ae/parity/main-reproduces-main/a/parity_netlist.json` | the w4ae commit; REQ-077's desk reading; the registry's HOT-R1 and fan-node choices; EQ-22 |
| `w4ae/parity/main-reproduces-main/a/parity_schematic.json` | `785d0297dafc79b7c6f22f72f9b4f0106e23bd314dce674116c445fcafa4fe70` | 351 | `fnd/w4ae` `drafts/w4ae/parity/main-reproduces-main/a/parity_schematic.json` | the w4ae commit; REQ-077's desk reading; the registry's HOT-R1 and fan-node choices; EQ-22 |
| `w4ae/parity/main-reproduces-main/a/regen.json` | `e52cd1bba140c58d88e7e7bc27a47595f27f1d0da297cc4d4cbefa2f28e72957` | 4563 | `fnd/w4ae` `drafts/w4ae/parity/main-reproduces-main/a/regen.json` | the w4ae commit; REQ-077's desk reading; the registry's HOT-R1 and fan-node choices; EQ-22 |
| `w4ae/parity/main-reproduces-main/e/net_compare.txt` | `908dcec73b7cd8e80273e4d2a5173297aa2c802367feea3cd604285dbba40f92` | 208 | `fnd/w4ae` `drafts/w4ae/parity/main-reproduces-main/e/net_compare.txt` | the w4ae commit; REQ-077's desk reading; the registry's HOT-R1 and fan-node choices; EQ-22 |
| `w4ae/parity/main-reproduces-main/e/parity_bom.json` | `09a7a85364829556cbc457c9d2050d8ae254742b3826ae1f6cd0e5f6843d8e9d` | 68 | `fnd/w4ae` `drafts/w4ae/parity/main-reproduces-main/e/parity_bom.json` | the w4ae commit; REQ-077's desk reading; the registry's HOT-R1 and fan-node choices; EQ-22 |
| `w4ae/parity/main-reproduces-main/e/parity_erc.json` | `14039c7eaa246a5d372faaa999955a9803064d52dda9825485f196cb129abaa2` | 353 | `fnd/w4ae` `drafts/w4ae/parity/main-reproduces-main/e/parity_erc.json` | the w4ae commit; REQ-077's desk reading; the registry's HOT-R1 and fan-node choices; EQ-22 |
| `w4ae/parity/main-reproduces-main/e/parity_intent.json` | `607f2e1b7adb75dc66267217a7334114126f37ea6ca8cab0548736b90c1ba3d4` | 76 | `fnd/w4ae` `drafts/w4ae/parity/main-reproduces-main/e/parity_intent.json` | the w4ae commit; REQ-077's desk reading; the registry's HOT-R1 and fan-node choices; EQ-22 |
| `w4ae/parity/main-reproduces-main/e/parity_netlist.json` | `420df24f1ac9c400df052701ae1659e624ad8251f8a4390966252cef315e9d2f` | 711 | `fnd/w4ae` `drafts/w4ae/parity/main-reproduces-main/e/parity_netlist.json` | the w4ae commit; REQ-077's desk reading; the registry's HOT-R1 and fan-node choices; EQ-22 |
| `w4ae/parity/main-reproduces-main/e/parity_schematic.json` | `ace929ea68219b80b5988bb0d9b42f9a99b6fdda1b7305c112faa594f6a07d7d` | 349 | `fnd/w4ae` `drafts/w4ae/parity/main-reproduces-main/e/parity_schematic.json` | the w4ae commit; REQ-077's desk reading; the registry's HOT-R1 and fan-node choices; EQ-22 |
| `w4ae/parity/main-reproduces-main/e/regen.json` | `211cbd3b7360ca317475f95a6cd86b49d6de62809617740bf13e0d32d68573d5` | 4779 | `fnd/w4ae` `drafts/w4ae/parity/main-reproduces-main/e/regen.json` | the w4ae commit; REQ-077's desk reading; the registry's HOT-R1 and fan-node choices; EQ-22 |
| `w4ae/post_docs_registry.py` | `8beacd078291e6c0607bcc4c9d62784ccec0c793fbca6ceaf5525f0ab82c3083` | 6498 | `fnd/w4ae` `drafts/w4ae/post_docs_registry.py` | the w4ae commit; REQ-077's desk reading; the registry's HOT-R1 and fan-node choices; EQ-22 |
| `w4ae/post_docs_registry_r8int6.py` | `9a0d7589ab19927640b79249660b03a30bac333392a00da2bc4a7350e5527b2e` | 6374 | the r8int6 integrator (`post_docs_registry_r8int6.py`) | the w4ae commit; REQ-077's desk reading; the registry's HOT-R1 and fan-node choices; EQ-22 |
| `w4ae/readings/after/pcb-a-power-a23/check_contracts.verdict.json` | `ffcc7da2cb66d9b01ae7d8cc45fa180d103051a00e037562e1bf7c6d60a14c38` | 2941 | `fnd/w4ae` `drafts/w4ae/readings/after/pcb-a-power-a23/check_contracts.verdict.json` | the w4ae commit; REQ-077's desk reading; the registry's HOT-R1 and fan-node choices; EQ-22 |
| `w4ae/readings/after/pcb-a-power-a23/check_contracts_a.verdict.json` | `fd29ba51cb61e2ad9a95093680b860d4f52ab5525833061477fe10442c437e9f` | 2693 | `fnd/w4ae` `drafts/w4ae/readings/after/pcb-a-power-a23/check_contracts_a.verdict.json` | the w4ae commit; REQ-077's desk reading; the registry's HOT-R1 and fan-node choices; EQ-22 |
| `w4ae/readings/after/pcb-a-power-a23/check_contracts_e.verdict.json` | `ceb9624df1dfa2d2fcab69ef6e21b6c94ff600cc0e7c392907d9b81bed59ac91` | 2165 | `fnd/w4ae` `drafts/w4ae/readings/after/pcb-a-power-a23/check_contracts_e.verdict.json` | the w4ae commit; REQ-077's desk reading; the registry's HOT-R1 and fan-node choices; EQ-22 |
| `w4ae/readings/after/pcb-a-power-a23/clock_check.verdict.json` | `db5594510f8ca0363ab2bae97350e35d6640ed7411ac87d60c18dafd3856ac94` | 1076 | `fnd/w4ae` `drafts/w4ae/readings/after/pcb-a-power-a23/clock_check.verdict.json` | the w4ae commit; REQ-077's desk reading; the registry's HOT-R1 and fan-node choices; EQ-22 |
| `w4ae/readings/after/pcb-a-power-a23/derate.verdict.json` | `b509cd6e58e9e676731db8359215fa50ad00aa1d7dd77c7a53e3c9478e79c172` | 1254 | `fnd/w4ae` `drafts/w4ae/readings/after/pcb-a-power-a23/derate.verdict.json` | the w4ae commit; REQ-077's desk reading; the registry's HOT-R1 and fan-node choices; EQ-22 |
| `w4ae/readings/after/pcb-a-power-a23/edge_length.verdict.json` | `d536328d23a3bd1a7abd32cb2356b45f9516450c0dffa9a4de5aaa6da480c3d6` | 9116 | `fnd/w4ae` `drafts/w4ae/readings/after/pcb-a-power-a23/edge_length.verdict.json` | the w4ae commit; REQ-077's desk reading; the registry's HOT-R1 and fan-node choices; EQ-22 |
| `w4ae/readings/after/pcb-a-power-a23/energy_chain_a.verdict.json` | `25227affbab0a6a33c53502fe6b3f482ff147422b4405e5f9286db3c229c34b9` | 1750 | `fnd/w4ae` `drafts/w4ae/readings/after/pcb-a-power-a23/energy_chain_a.verdict.json` | the w4ae commit; REQ-077's desk reading; the registry's HOT-R1 and fan-node choices; EQ-22 |
| `w4ae/readings/after/pcb-a-power-a23/energy_chain_e.verdict.json` | `3fa9b31bc05c3037eee6157cd105ed5c74f539662ce872fddce0f486b4563fa5` | 1750 | `fnd/w4ae` `drafts/w4ae/readings/after/pcb-a-power-a23/energy_chain_e.verdict.json` | the w4ae commit; REQ-077's desk reading; the registry's HOT-R1 and fan-node choices; EQ-22 |
| `w4ae/readings/after/pcb-a-power-a23/erc_gate.verdict.json` | `763869ca1355d2ab927a5deca271b96533a73cbdd906f14554b2fded8601a8de` | 1724 | `fnd/w4ae` `drafts/w4ae/readings/after/pcb-a-power-a23/erc_gate.verdict.json` | the w4ae commit; REQ-077's desk reading; the registry's HOT-R1 and fan-node choices; EQ-22 |
| `w4ae/readings/after/pcb-a-power-a23/inhibit_chain_a.verdict.json` | `586191d6be4507779cac4b8243118dbab5de86e10f18fc7ab27b72be6d9ba6d0` | 3995 | `fnd/w4ae` `drafts/w4ae/readings/after/pcb-a-power-a23/inhibit_chain_a.verdict.json` | the w4ae commit; REQ-077's desk reading; the registry's HOT-R1 and fan-node choices; EQ-22 |
| `w4ae/readings/after/pcb-a-power-a23/inhibit_chain_e.verdict.json` | `a12133e5e3be9a291d5938bf98e05e3c3bfe29c267a5d07d1994ffa750919733` | 2901 | `fnd/w4ae` `drafts/w4ae/readings/after/pcb-a-power-a23/inhibit_chain_e.verdict.json` | the w4ae commit; REQ-077's desk reading; the registry's HOT-R1 and fan-node choices; EQ-22 |
| `w4ae/readings/after/pcb-a-power-a23/intent_rails.verdict.json` | `1cd870a968ff98777ea96af85dbc21f67d0520c38f7e533038b6175f368ef7f2` | 11046 | `fnd/w4ae` `drafts/w4ae/readings/after/pcb-a-power-a23/intent_rails.verdict.json` | the w4ae commit; REQ-077's desk reading; the registry's HOT-R1 and fan-node choices; EQ-22 |
| `w4ae/readings/after/pcb-a-power-a23/interfaces_a.verdict.json` | `497eced498224c38f576e1d087fe57416fb7260e9407a663fb3e70c60463915b` | 1627 | `fnd/w4ae` `drafts/w4ae/readings/after/pcb-a-power-a23/interfaces_a.verdict.json` | the w4ae commit; REQ-077's desk reading; the registry's HOT-R1 and fan-node choices; EQ-22 |
| `w4ae/readings/after/pcb-a-power-a23/interfaces_e.verdict.json` | `14c0ed4dd6a2770d6584a6df8b2b8acd4fe4f55575b144ae4f5b560919057d15` | 1625 | `fnd/w4ae` `drafts/w4ae/readings/after/pcb-a-power-a23/interfaces_e.verdict.json` | the w4ae commit; REQ-077's desk reading; the registry's HOT-R1 and fan-node choices; EQ-22 |
| `w4ae/readings/after/pcb-a-power-a23/pin_map_lands_a.verdict.json` | `e2faf100cc490efc3273317df75e988eff1379db14ecc4de4524a7a519cb0538` | 1250 | `fnd/w4ae` `drafts/w4ae/readings/after/pcb-a-power-a23/pin_map_lands_a.verdict.json` | the w4ae commit; REQ-077's desk reading; the registry's HOT-R1 and fan-node choices; EQ-22 |
| `w4ae/readings/after/pcb-a-power-a23/port_protect_a.verdict.json` | `b54ebed739808fc95b3e473c9060311d3e0d968b1aad6ecf19ca9470a5fe201f` | 1758 | `fnd/w4ae` `drafts/w4ae/readings/after/pcb-a-power-a23/port_protect_a.verdict.json` | the w4ae commit; REQ-077's desk reading; the registry's HOT-R1 and fan-node choices; EQ-22 |
| `w4ae/readings/after/pcb-a-power-a23/power_sequence.verdict.json` | `1fdf6d26dc0934c52221f4e9bc8189790bd9fc618a4a897b77424c8a3aafecaa` | 1698 | `fnd/w4ae` `drafts/w4ae/readings/after/pcb-a-power-a23/power_sequence.verdict.json` | the w4ae commit; REQ-077's desk reading; the registry's HOT-R1 and fan-node choices; EQ-22 |
| `w4ae/readings/after/pcb-a-power-a23/safe_lines_a.verdict.json` | `996d69941ea65fcd998b9fb3c737b80832cf13e7c7d6b76aa37c3e56b3832c59` | 2744 | `fnd/w4ae` `drafts/w4ae/readings/after/pcb-a-power-a23/safe_lines_a.verdict.json` | the w4ae commit; REQ-077's desk reading; the registry's HOT-R1 and fan-node choices; EQ-22 |
| `w4ae/readings/after/pcb-e1-dock-e7/check_contracts.verdict.json` | `272fbf3028332fc19d676823f8533efb5bc194a8d058e625be4b5003cfc7e44e` | 2941 | `fnd/w4ae` `drafts/w4ae/readings/after/pcb-e1-dock-e7/check_contracts.verdict.json` | the w4ae commit; REQ-077's desk reading; the registry's HOT-R1 and fan-node choices; EQ-22 |
| `w4ae/readings/after/pcb-e1-dock-e7/check_contracts_a.verdict.json` | `810bdcda96fbaa4da767a152cef9e63d84e5741bb26a12bb1a477bc29d239f3c` | 2693 | `fnd/w4ae` `drafts/w4ae/readings/after/pcb-e1-dock-e7/check_contracts_a.verdict.json` | the w4ae commit; REQ-077's desk reading; the registry's HOT-R1 and fan-node choices; EQ-22 |
| `w4ae/readings/after/pcb-e1-dock-e7/check_contracts_e.verdict.json` | `1c06f1190bc380ff7aa359f38ce81ac1d1e1051903de54ff74b0d40aeb88fe3f` | 2165 | `fnd/w4ae` `drafts/w4ae/readings/after/pcb-e1-dock-e7/check_contracts_e.verdict.json` | the w4ae commit; REQ-077's desk reading; the registry's HOT-R1 and fan-node choices; EQ-22 |
| `w4ae/readings/after/pcb-e1-dock-e7/clock_check.verdict.json` | `2e8818969009e27e1a4da5ae638d2a5e128d35f31dbe1e2eeadc470cb209628a` | 1219 | `fnd/w4ae` `drafts/w4ae/readings/after/pcb-e1-dock-e7/clock_check.verdict.json` | the w4ae commit; REQ-077's desk reading; the registry's HOT-R1 and fan-node choices; EQ-22 |
| `w4ae/readings/after/pcb-e1-dock-e7/derate.verdict.json` | `9f69a86bc690009413f99d293542bc4070925f2d2a78b7837ebe9350b395bfc4` | 1251 | `fnd/w4ae` `drafts/w4ae/readings/after/pcb-e1-dock-e7/derate.verdict.json` | the w4ae commit; REQ-077's desk reading; the registry's HOT-R1 and fan-node choices; EQ-22 |
| `w4ae/readings/after/pcb-e1-dock-e7/edge_length.verdict.json` | `ba3699eb8946c4c70fd672979370b3712e50b86d6118718a9a0670ffe616a48d` | 7784 | `fnd/w4ae` `drafts/w4ae/readings/after/pcb-e1-dock-e7/edge_length.verdict.json` | the w4ae commit; REQ-077's desk reading; the registry's HOT-R1 and fan-node choices; EQ-22 |
| `w4ae/readings/after/pcb-e1-dock-e7/energy_chain_a.verdict.json` | `4beb7fe014511fac58c4d97ed2ce862e0f6569f5ea0911a3b24f1533ad9d5767` | 1750 | `fnd/w4ae` `drafts/w4ae/readings/after/pcb-e1-dock-e7/energy_chain_a.verdict.json` | the w4ae commit; REQ-077's desk reading; the registry's HOT-R1 and fan-node choices; EQ-22 |
| `w4ae/readings/after/pcb-e1-dock-e7/energy_chain_e.verdict.json` | `c67497ac9b9ea223e990bb48273fecbcdbca7123eca80aa51919aff0f3127bb5` | 1750 | `fnd/w4ae` `drafts/w4ae/readings/after/pcb-e1-dock-e7/energy_chain_e.verdict.json` | the w4ae commit; REQ-077's desk reading; the registry's HOT-R1 and fan-node choices; EQ-22 |
| `w4ae/readings/after/pcb-e1-dock-e7/erc_gate.verdict.json` | `6a6807b26e1257f77154a7d10f260b3142959c9c853ed87b4fe97a6c1575e7ec` | 1722 | `fnd/w4ae` `drafts/w4ae/readings/after/pcb-e1-dock-e7/erc_gate.verdict.json` | the w4ae commit; REQ-077's desk reading; the registry's HOT-R1 and fan-node choices; EQ-22 |
| `w4ae/readings/after/pcb-e1-dock-e7/inhibit_chain_a.verdict.json` | `f04ebf43f76eb215339f725cb728ce3f45c5065a65589c5b3a5c821f2854e645` | 3995 | `fnd/w4ae` `drafts/w4ae/readings/after/pcb-e1-dock-e7/inhibit_chain_a.verdict.json` | the w4ae commit; REQ-077's desk reading; the registry's HOT-R1 and fan-node choices; EQ-22 |
| `w4ae/readings/after/pcb-e1-dock-e7/inhibit_chain_e.verdict.json` | `e16272abaa9bc37da6d03fbb693456799700aa5b859f06de0b52d8a9a1ea28ba` | 2901 | `fnd/w4ae` `drafts/w4ae/readings/after/pcb-e1-dock-e7/inhibit_chain_e.verdict.json` | the w4ae commit; REQ-077's desk reading; the registry's HOT-R1 and fan-node choices; EQ-22 |
| `w4ae/readings/after/pcb-e1-dock-e7/intent_rails.verdict.json` | `4a59afb1fe3a12e2019736b3862841f578ff14a06bacff60afc27e4ce07220be` | 7444 | `fnd/w4ae` `drafts/w4ae/readings/after/pcb-e1-dock-e7/intent_rails.verdict.json` | the w4ae commit; REQ-077's desk reading; the registry's HOT-R1 and fan-node choices; EQ-22 |
| `w4ae/readings/after/pcb-e1-dock-e7/interfaces_a.verdict.json` | `21be2cf4fa6e0f6076069950dd5bb9b35861583416eaf0ac60956e0828166446` | 1627 | `fnd/w4ae` `drafts/w4ae/readings/after/pcb-e1-dock-e7/interfaces_a.verdict.json` | the w4ae commit; REQ-077's desk reading; the registry's HOT-R1 and fan-node choices; EQ-22 |
| `w4ae/readings/after/pcb-e1-dock-e7/interfaces_e.verdict.json` | `b3acd95ae9aa03f91a63d4eaf32399a7ceded2113b3c9d18a54e7cb5e0261d56` | 1625 | `fnd/w4ae` `drafts/w4ae/readings/after/pcb-e1-dock-e7/interfaces_e.verdict.json` | the w4ae commit; REQ-077's desk reading; the registry's HOT-R1 and fan-node choices; EQ-22 |
| `w4ae/readings/after/pcb-e1-dock-e7/pin_map_lands_e.verdict.json` | `1de611fb1448bb41d40038a4ed6a7062266a433222f9269f552f006a00c2aaf3` | 1251 | `fnd/w4ae` `drafts/w4ae/readings/after/pcb-e1-dock-e7/pin_map_lands_e.verdict.json` | the w4ae commit; REQ-077's desk reading; the registry's HOT-R1 and fan-node choices; EQ-22 |
| `w4ae/readings/after/pcb-e1-dock-e7/port_protect_e.verdict.json` | `874f1a4484823eecde507033a24852d40acf0afe36d65705266f63880ef96421` | 1758 | `fnd/w4ae` `drafts/w4ae/readings/after/pcb-e1-dock-e7/port_protect_e.verdict.json` | the w4ae commit; REQ-077's desk reading; the registry's HOT-R1 and fan-node choices; EQ-22 |
| `w4ae/readings/after/pcb-e1-dock-e7/power_sequence.verdict.json` | `29e3933a753c555328ce93f60592ae9950de2ab00de230209853077907eb98aa` | 1697 | `fnd/w4ae` `drafts/w4ae/readings/after/pcb-e1-dock-e7/power_sequence.verdict.json` | the w4ae commit; REQ-077's desk reading; the registry's HOT-R1 and fan-node choices; EQ-22 |
| `w4ae/readings/after/pcb-e1-dock-e7/safe_lines_e.verdict.json` | `3fe8ffcb1b2f0d7b6486789e66057bba2df4dcab6000764c5dbd5a333fb07a77` | 1928 | `fnd/w4ae` `drafts/w4ae/readings/after/pcb-e1-dock-e7/safe_lines_e.verdict.json` | the w4ae commit; REQ-077's desk reading; the registry's HOT-R1 and fan-node choices; EQ-22 |
| `w4ae/readings/before-after-summary.txt` | `7ef107c969876fb56f1111542f3dadd46b273eebf86df6c136716b695bb59218` | 7464 | `fnd/w4ae` `drafts/w4ae/readings/before-after-summary.txt` | the w4ae commit; REQ-077's desk reading; the registry's HOT-R1 and fan-node choices; EQ-22 |
| `w4ae/readings/before/pcb-a-power-a23/check_contracts.verdict.json` | `712524a8f6c27acda4b17bceb60c6e08f0463f65e15ca1cf71658721cf3b8a03` | 2941 | `fnd/w4ae` `drafts/w4ae/readings/before/pcb-a-power-a23/check_contracts.verdict.json` | the w4ae commit; REQ-077's desk reading; the registry's HOT-R1 and fan-node choices; EQ-22 |
| `w4ae/readings/before/pcb-a-power-a23/check_contracts_a.verdict.json` | `b2d9e6999e1f0fb1006142e42208999f3943a155a631f335a5baa36d05b4e8bd` | 2693 | `fnd/w4ae` `drafts/w4ae/readings/before/pcb-a-power-a23/check_contracts_a.verdict.json` | the w4ae commit; REQ-077's desk reading; the registry's HOT-R1 and fan-node choices; EQ-22 |
| `w4ae/readings/before/pcb-a-power-a23/check_contracts_e.verdict.json` | `39e27b2a41333ee260ba3825a557b2b0b922daa49e4e20daaac04613dc51fbaa` | 2165 | `fnd/w4ae` `drafts/w4ae/readings/before/pcb-a-power-a23/check_contracts_e.verdict.json` | the w4ae commit; REQ-077's desk reading; the registry's HOT-R1 and fan-node choices; EQ-22 |
| `w4ae/readings/before/pcb-a-power-a23/clock_check.verdict.json` | `4f1e935253328cbdc139b1ea8f88d9c076d531c1d76ec43b99fb18482f887e69` | 1076 | `fnd/w4ae` `drafts/w4ae/readings/before/pcb-a-power-a23/clock_check.verdict.json` | the w4ae commit; REQ-077's desk reading; the registry's HOT-R1 and fan-node choices; EQ-22 |
| `w4ae/readings/before/pcb-a-power-a23/derate.verdict.json` | `dcef93e1185db5ab5fcc2a6f0883724eb3902ba6f84a6a7e40f0ab3a78733f2c` | 1254 | `fnd/w4ae` `drafts/w4ae/readings/before/pcb-a-power-a23/derate.verdict.json` | the w4ae commit; REQ-077's desk reading; the registry's HOT-R1 and fan-node choices; EQ-22 |
| `w4ae/readings/before/pcb-a-power-a23/edge_length.verdict.json` | `88e265eb6fe53c99688a4bf0e372c156c9b91da396840d9783c3cd343a60722a` | 9116 | `fnd/w4ae` `drafts/w4ae/readings/before/pcb-a-power-a23/edge_length.verdict.json` | the w4ae commit; REQ-077's desk reading; the registry's HOT-R1 and fan-node choices; EQ-22 |
| `w4ae/readings/before/pcb-a-power-a23/energy_chain_a.verdict.json` | `8d8b3c8e7afbc9cdd480bd275ce3ee54705242bf4e39a8f5e035cb73cc474aa3` | 1750 | `fnd/w4ae` `drafts/w4ae/readings/before/pcb-a-power-a23/energy_chain_a.verdict.json` | the w4ae commit; REQ-077's desk reading; the registry's HOT-R1 and fan-node choices; EQ-22 |
| `w4ae/readings/before/pcb-a-power-a23/energy_chain_e.verdict.json` | `7b2e4ae5e21e3b91a4ab05123410f60a386d2ee8be43dbb23086c291a54205f5` | 1750 | `fnd/w4ae` `drafts/w4ae/readings/before/pcb-a-power-a23/energy_chain_e.verdict.json` | the w4ae commit; REQ-077's desk reading; the registry's HOT-R1 and fan-node choices; EQ-22 |
| `w4ae/readings/before/pcb-a-power-a23/erc_gate.verdict.json` | `476f5e83b063f10c839b3db05aa510b36e5cb69f2d6358368afa81121a71b24f` | 1724 | `fnd/w4ae` `drafts/w4ae/readings/before/pcb-a-power-a23/erc_gate.verdict.json` | the w4ae commit; REQ-077's desk reading; the registry's HOT-R1 and fan-node choices; EQ-22 |
| `w4ae/readings/before/pcb-a-power-a23/inhibit_chain_a.verdict.json` | `ad78816f1e96d7af2f9be391d724d70c83e794b9416ec77575c6cbd64a50cd65` | 3995 | `fnd/w4ae` `drafts/w4ae/readings/before/pcb-a-power-a23/inhibit_chain_a.verdict.json` | the w4ae commit; REQ-077's desk reading; the registry's HOT-R1 and fan-node choices; EQ-22 |
| `w4ae/readings/before/pcb-a-power-a23/inhibit_chain_e.verdict.json` | `714ddd44b85716e4ede53418de244f58f1b8b22f8f4813ea5f409b0373acb749` | 2901 | `fnd/w4ae` `drafts/w4ae/readings/before/pcb-a-power-a23/inhibit_chain_e.verdict.json` | the w4ae commit; REQ-077's desk reading; the registry's HOT-R1 and fan-node choices; EQ-22 |
| `w4ae/readings/before/pcb-a-power-a23/intent_rails.verdict.json` | `f0861c10e93ec0e973db366e3f30e64917fbfba6b3d1c925f156c3ca8a6ba712` | 11046 | `fnd/w4ae` `drafts/w4ae/readings/before/pcb-a-power-a23/intent_rails.verdict.json` | the w4ae commit; REQ-077's desk reading; the registry's HOT-R1 and fan-node choices; EQ-22 |
| `w4ae/readings/before/pcb-a-power-a23/interfaces_a.verdict.json` | `fb4073bd232195849105d626c5d1443eb209621ca4fbe346eba8f8fbf5808c60` | 1627 | `fnd/w4ae` `drafts/w4ae/readings/before/pcb-a-power-a23/interfaces_a.verdict.json` | the w4ae commit; REQ-077's desk reading; the registry's HOT-R1 and fan-node choices; EQ-22 |
| `w4ae/readings/before/pcb-a-power-a23/interfaces_e.verdict.json` | `9a90d2b60e87c3d7609d5e89de5be7a842449784287ed12f451ae9717af9365d` | 1625 | `fnd/w4ae` `drafts/w4ae/readings/before/pcb-a-power-a23/interfaces_e.verdict.json` | the w4ae commit; REQ-077's desk reading; the registry's HOT-R1 and fan-node choices; EQ-22 |
| `w4ae/readings/before/pcb-a-power-a23/pin_map_lands_a.verdict.json` | `ead2d07bfe27ef48c49c40ea0df678242a9680bc8ed6c819ea4e6b4b515835dc` | 1250 | `fnd/w4ae` `drafts/w4ae/readings/before/pcb-a-power-a23/pin_map_lands_a.verdict.json` | the w4ae commit; REQ-077's desk reading; the registry's HOT-R1 and fan-node choices; EQ-22 |
| `w4ae/readings/before/pcb-a-power-a23/port_protect_a.verdict.json` | `32cb8582277111c8a884b5c5fd85e7119439da1152874e3c2a5c3a0ce695cf6a` | 1758 | `fnd/w4ae` `drafts/w4ae/readings/before/pcb-a-power-a23/port_protect_a.verdict.json` | the w4ae commit; REQ-077's desk reading; the registry's HOT-R1 and fan-node choices; EQ-22 |
| `w4ae/readings/before/pcb-a-power-a23/power_sequence.verdict.json` | `4ea7dd4186c4cfff58b9655215919af79fa93b1385ecbf882618615742c1a6a4` | 1698 | `fnd/w4ae` `drafts/w4ae/readings/before/pcb-a-power-a23/power_sequence.verdict.json` | the w4ae commit; REQ-077's desk reading; the registry's HOT-R1 and fan-node choices; EQ-22 |
| `w4ae/readings/before/pcb-a-power-a23/safe_lines_a.verdict.json` | `609614796c3f9f0d3cd0010aa7758b039dee7187476fc657a3bb84748c9849a3` | 2583 | `fnd/w4ae` `drafts/w4ae/readings/before/pcb-a-power-a23/safe_lines_a.verdict.json` | the w4ae commit; REQ-077's desk reading; the registry's HOT-R1 and fan-node choices; EQ-22 |
| `w4ae/readings/before/pcb-e1-dock-e7/check_contracts.verdict.json` | `d17f76d50056e1cb3c3f2f88d84d35fa00f7a4ca6fb1496c15505b7e74ffa5c9` | 2941 | `fnd/w4ae` `drafts/w4ae/readings/before/pcb-e1-dock-e7/check_contracts.verdict.json` | the w4ae commit; REQ-077's desk reading; the registry's HOT-R1 and fan-node choices; EQ-22 |
| `w4ae/readings/before/pcb-e1-dock-e7/check_contracts_a.verdict.json` | `2de6e92dd8ae23bf47598382241eb328aeb71bb8ca5dada6e1c4fdf5755379ce` | 2693 | `fnd/w4ae` `drafts/w4ae/readings/before/pcb-e1-dock-e7/check_contracts_a.verdict.json` | the w4ae commit; REQ-077's desk reading; the registry's HOT-R1 and fan-node choices; EQ-22 |
| `w4ae/readings/before/pcb-e1-dock-e7/check_contracts_e.verdict.json` | `85d84b7a647bf1da37dd717b8970893934e6cebf29c5b33ebbb778a42d2a1549` | 2165 | `fnd/w4ae` `drafts/w4ae/readings/before/pcb-e1-dock-e7/check_contracts_e.verdict.json` | the w4ae commit; REQ-077's desk reading; the registry's HOT-R1 and fan-node choices; EQ-22 |
| `w4ae/readings/before/pcb-e1-dock-e7/clock_check.verdict.json` | `0efd0da0a8195c14b6955e9d44179ecb14fc5a19ade7ce9e1e3af0d68317e2f8` | 1219 | `fnd/w4ae` `drafts/w4ae/readings/before/pcb-e1-dock-e7/clock_check.verdict.json` | the w4ae commit; REQ-077's desk reading; the registry's HOT-R1 and fan-node choices; EQ-22 |
| `w4ae/readings/before/pcb-e1-dock-e7/derate.verdict.json` | `6d9fac4138ee47b352a18e7ba597a468a31830149f934fdf6318ac5c06cd9d47` | 1251 | `fnd/w4ae` `drafts/w4ae/readings/before/pcb-e1-dock-e7/derate.verdict.json` | the w4ae commit; REQ-077's desk reading; the registry's HOT-R1 and fan-node choices; EQ-22 |
| `w4ae/readings/before/pcb-e1-dock-e7/edge_length.verdict.json` | `2a8beb0f050424a8a9aeedbd3c747ce8a603fb4163be5498e321cee68db3088a` | 7784 | `fnd/w4ae` `drafts/w4ae/readings/before/pcb-e1-dock-e7/edge_length.verdict.json` | the w4ae commit; REQ-077's desk reading; the registry's HOT-R1 and fan-node choices; EQ-22 |
| `w4ae/readings/before/pcb-e1-dock-e7/energy_chain_a.verdict.json` | `9f0127412dcdf2e589b8930b78184aed8bf55ccaf8a535ffab1769a231ff462d` | 1750 | `fnd/w4ae` `drafts/w4ae/readings/before/pcb-e1-dock-e7/energy_chain_a.verdict.json` | the w4ae commit; REQ-077's desk reading; the registry's HOT-R1 and fan-node choices; EQ-22 |
| `w4ae/readings/before/pcb-e1-dock-e7/energy_chain_e.verdict.json` | `a7a6c24f1a2d1ea4986a616a136bb5d0adb4073790b43a2ba43f3ee61574422c` | 1750 | `fnd/w4ae` `drafts/w4ae/readings/before/pcb-e1-dock-e7/energy_chain_e.verdict.json` | the w4ae commit; REQ-077's desk reading; the registry's HOT-R1 and fan-node choices; EQ-22 |
| `w4ae/readings/before/pcb-e1-dock-e7/erc_gate.verdict.json` | `8f87cbabdc0ce05d26712a4dbeac39c4ab2bcde634d46530de9c75cc55734a66` | 1722 | `fnd/w4ae` `drafts/w4ae/readings/before/pcb-e1-dock-e7/erc_gate.verdict.json` | the w4ae commit; REQ-077's desk reading; the registry's HOT-R1 and fan-node choices; EQ-22 |
| `w4ae/readings/before/pcb-e1-dock-e7/inhibit_chain_a.verdict.json` | `71a275e965542723e9df736321fa29322b0b97afd3cfc635b6d35687a6c1da12` | 3995 | `fnd/w4ae` `drafts/w4ae/readings/before/pcb-e1-dock-e7/inhibit_chain_a.verdict.json` | the w4ae commit; REQ-077's desk reading; the registry's HOT-R1 and fan-node choices; EQ-22 |
| `w4ae/readings/before/pcb-e1-dock-e7/inhibit_chain_e.verdict.json` | `ca6ed78f22fb19a50d73b22d157fdca2c2ae7f05f88515ba0a5317509c9bb12b` | 2901 | `fnd/w4ae` `drafts/w4ae/readings/before/pcb-e1-dock-e7/inhibit_chain_e.verdict.json` | the w4ae commit; REQ-077's desk reading; the registry's HOT-R1 and fan-node choices; EQ-22 |
| `w4ae/readings/before/pcb-e1-dock-e7/intent_rails.verdict.json` | `18554160a4d60ec39f2bb7e3185be74a90efc4839fcddd0748baa9c64f79b4af` | 7992 | `fnd/w4ae` `drafts/w4ae/readings/before/pcb-e1-dock-e7/intent_rails.verdict.json` | the w4ae commit; REQ-077's desk reading; the registry's HOT-R1 and fan-node choices; EQ-22 |
| `w4ae/readings/before/pcb-e1-dock-e7/interfaces_a.verdict.json` | `d359c96f160ec37126b3cfc366232270adb09697459930dc4daff4772491c4ab` | 1627 | `fnd/w4ae` `drafts/w4ae/readings/before/pcb-e1-dock-e7/interfaces_a.verdict.json` | the w4ae commit; REQ-077's desk reading; the registry's HOT-R1 and fan-node choices; EQ-22 |
| `w4ae/readings/before/pcb-e1-dock-e7/interfaces_e.verdict.json` | `a85eecf9c4777b7de29ff701967a61fabe4039938692be01cff4fec24da6af8c` | 1625 | `fnd/w4ae` `drafts/w4ae/readings/before/pcb-e1-dock-e7/interfaces_e.verdict.json` | the w4ae commit; REQ-077's desk reading; the registry's HOT-R1 and fan-node choices; EQ-22 |
| `w4ae/readings/before/pcb-e1-dock-e7/pin_map_lands_e.verdict.json` | `80ae418c2cd6cbba711350c55485518fbaf5be9d28d6576caf476b174e3543e4` | 1251 | `fnd/w4ae` `drafts/w4ae/readings/before/pcb-e1-dock-e7/pin_map_lands_e.verdict.json` | the w4ae commit; REQ-077's desk reading; the registry's HOT-R1 and fan-node choices; EQ-22 |
| `w4ae/readings/before/pcb-e1-dock-e7/port_protect_e.verdict.json` | `c699ec5254d2d799eb43f60df616534baf99cf473611d9cf80ac8757accb08e3` | 1758 | `fnd/w4ae` `drafts/w4ae/readings/before/pcb-e1-dock-e7/port_protect_e.verdict.json` | the w4ae commit; REQ-077's desk reading; the registry's HOT-R1 and fan-node choices; EQ-22 |
| `w4ae/readings/before/pcb-e1-dock-e7/power_sequence.verdict.json` | `52b0261664611c8fc69644e46ca633dd057cb8fd3af0e852b0a5a174aa6f438e` | 1697 | `fnd/w4ae` `drafts/w4ae/readings/before/pcb-e1-dock-e7/power_sequence.verdict.json` | the w4ae commit; REQ-077's desk reading; the registry's HOT-R1 and fan-node choices; EQ-22 |
| `w4ae/readings/before/pcb-e1-dock-e7/safe_lines_e.verdict.json` | `bc1f931ed6983d3cc619ecff60932b2b9b496dc8489e6b0ee095a319beeeff0b` | 1784 | `fnd/w4ae` `drafts/w4ae/readings/before/pcb-e1-dock-e7/safe_lines_e.verdict.json` | the w4ae commit; REQ-077's desk reading; the registry's HOT-R1 and fan-node choices; EQ-22 |
| `w4ae/readings/hot_r1_trace-candidate.txt` | `fc2caf96fc65eeb3816c43a4ecf6682e6f28c0fdd263d5f8fa6898c03f5dda52` | 5508 | `fnd/w4ae` `drafts/w4ae/readings/hot_r1_trace-candidate.txt` | the w4ae commit; REQ-077's desk reading; the registry's HOT-R1 and fan-node choices; EQ-22 |
| `w4ae/readings/hot_r1_trace-main-91894cd7.txt` | `8058d23dc87a8ebd49c0f4ffbd1c3c519ba44721ab954f924f35c3fe417f8ed5` | 5222 | `fnd/w4ae` `drafts/w4ae/readings/hot_r1_trace-main-91894cd7.txt` | the w4ae commit; REQ-077's desk reading; the registry's HOT-R1 and fan-node choices; EQ-22 |
| `w4ae/readings/rt-after-a.log` | `d0f6735f7a54de93c71b4b18abf30e3a2b7ab3054f5a8166e03fc495bfa39426` | 3527 | `fnd/w4ae` `drafts/w4ae/readings/rt-after-a.log` | the w4ae commit; REQ-077's desk reading; the registry's HOT-R1 and fan-node choices; EQ-22 |
| `w4ae/readings/rt-after-e.log` | `5132b80dcfda833b2ced7cec7dbb195dbd15965e33bca26d210cbd2bfe724126` | 3507 | `fnd/w4ae` `drafts/w4ae/readings/rt-after-e.log` | the w4ae commit; REQ-077's desk reading; the registry's HOT-R1 and fan-node choices; EQ-22 |
| `w4ae/readings/rt-before-a.log` | `2347aa97e85f3941b4d8e6354bd26a188c29a0301c42536c0b68c36d5a7c756b` | 3531 | `fnd/w4ae` `drafts/w4ae/readings/rt-before-a.log` | the w4ae commit; REQ-077's desk reading; the registry's HOT-R1 and fan-node choices; EQ-22 |
| `w4ae/readings/rt-before-e.log` | `96d59fb01c993c8ae9aef51a394e4d1ad1d7313ea88eda07324e56535b88fba4` | 3527 | `fnd/w4ae` `drafts/w4ae/readings/rt-before-e.log` | the w4ae commit; REQ-077's desk reading; the registry's HOT-R1 and fan-node choices; EQ-22 |
| `w4ae/readings/tests-final.log` | `13bf417fa97a11a27574f4935d71ea59d8ef98ea0ed21eefdb349e583a8ae2c8` | 59764 | `fnd/w4ae` `drafts/w4ae/readings/tests-final.log` | the w4ae commit; REQ-077's desk reading; the registry's HOT-R1 and fan-node choices; EQ-22 |
| `w4b/apply_registry.py` | `383673dbe1cdc3434d0ad4129f2f8ad54eed9e70784cae1f18ce8e06db4d3652` | 23121 | `fnd/w4b` `drafts/w4b/apply_registry.py` | the w4b commit; `EMCON.md` section 4c; the registry's W4B-D1 to W4B-D3 choices and RF-002 instrument item |
| `w4b/apply_registry_r8int6.py` | `2cb79b1021a3089bc88a35fbaf4f3ccd16ed1318ecd2e3e180ef41ca5526f545` | 25170 | the r8int6 integrator (`apply_registry_r8int6.py`) | the w4b commit; `EMCON.md` section 4c; the registry's W4B-D1 to W4B-D3 choices and RF-002 instrument item |
| `w4b/apply_w4b_r8int6.sh` | `ec9ff5c7c31f5b541e37c20b8f73e9cff513e0ea4110664cf345a5cf892b490f` | 1705 | the r8int6 integrator (`apply_w4b_r8int6.sh`) | the w4b commit; `EMCON.md` section 4c; the registry's W4B-D1 to W4B-D3 choices and RF-002 instrument item |
| `w4b/evidence/box/compare.log` | `927421392a94203093b4cc7a329ada1d0d60fb9bff47c8c0a0f51078f80f65ed` | 2058 | `fnd/w4b` `drafts/w4b/evidence/box/compare.log` | the w4b commit; `EMCON.md` section 4c; the registry's W4B-D1 to W4B-D3 choices and RF-002 instrument item |
| `w4b/evidence/box/compare/base_vs_committed_bom.json` | `da4625a57a36e599c5d9cff640a216be0efc29eba0bde764cdfa3069a6c3dd0c` | 68 | `fnd/w4b` `drafts/w4b/evidence/box/compare/base_vs_committed_bom.json` | the w4b commit; `EMCON.md` section 4c; the registry's W4B-D1 to W4B-D3 choices and RF-002 instrument item |
| `w4b/evidence/box/compare/base_vs_committed_erc.json` | `58fbc1bb13978469fa5d013f5d380cda77cac95f7866f35fc349937a028496de` | 485 | `fnd/w4b` `drafts/w4b/evidence/box/compare/base_vs_committed_erc.json` | the w4b commit; `EMCON.md` section 4c; the registry's W4B-D1 to W4B-D3 choices and RF-002 instrument item |
| `w4b/evidence/box/compare/base_vs_committed_intent.json` | `607f2e1b7adb75dc66267217a7334114126f37ea6ca8cab0548736b90c1ba3d4` | 76 | `fnd/w4b` `drafts/w4b/evidence/box/compare/base_vs_committed_intent.json` | the w4b commit; `EMCON.md` section 4c; the registry's W4B-D1 to W4B-D3 choices and RF-002 instrument item |
| `w4b/evidence/box/compare/base_vs_committed_netlist.json` | `67025d92444f75bf4127e5a8f1743325d9008d8f4b960a547c298a3065ee5b00` | 716 | `fnd/w4b` `drafts/w4b/evidence/box/compare/base_vs_committed_netlist.json` | the w4b commit; `EMCON.md` section 4c; the registry's W4B-D1 to W4B-D3 choices and RF-002 instrument item |
| `w4b/evidence/box/compare/base_vs_committed_provenance.json` | `beaf5c58de8d3847e983c2730098b050055c47053475cde02de9a08d3210df35` | 80 | `fnd/w4b` `drafts/w4b/evidence/box/compare/base_vs_committed_provenance.json` | the w4b commit; `EMCON.md` section 4c; the registry's W4B-D1 to W4B-D3 choices and RF-002 instrument item |
| `w4b/evidence/box/compare/base_vs_committed_schematic.json` | `ae0669e008778caeef8abacf82b910c30b6718d65ac96ed67c81e066696088a0` | 351 | `fnd/w4b` `drafts/w4b/evidence/box/compare/base_vs_committed_schematic.json` | the w4b commit; `EMCON.md` section 4c; the registry's W4B-D1 to W4B-D3 choices and RF-002 instrument item |
| `w4b/evidence/box/compare/cand_vs_base_bom.json` | `109ee34983e734a476c005baee7d4cd7f6d4168bec16b4c668502f50b2d754bc` | 5163 | `fnd/w4b` `drafts/w4b/evidence/box/compare/cand_vs_base_bom.json` | the w4b commit; `EMCON.md` section 4c; the registry's W4B-D1 to W4B-D3 choices and RF-002 instrument item |
| `w4b/evidence/box/compare/cand_vs_base_erc.json` | `42e87f1edcc5ba068e30ce4a8a8671c834dbd7893d1533605c84f1e2e244bd69` | 10751 | `fnd/w4b` `drafts/w4b/evidence/box/compare/cand_vs_base_erc.json` | the w4b commit; `EMCON.md` section 4c; the registry's W4B-D1 to W4B-D3 choices and RF-002 instrument item |
| `w4b/evidence/box/compare/cand_vs_base_intent.json` | `fa9c8b0e9fd1ee122ca6a739a42e7da37df5bf92e8c1d33bd96fdd83b7ea37c3` | 91 | `fnd/w4b` `drafts/w4b/evidence/box/compare/cand_vs_base_intent.json` | the w4b commit; `EMCON.md` section 4c; the registry's W4B-D1 to W4B-D3 choices and RF-002 instrument item |
| `w4b/evidence/box/compare/cand_vs_base_netlist.json` | `ae7dd67b0a0fdc564729874486d030785fd521327cf39f4093f131274274f321` | 12453 | `fnd/w4b` `drafts/w4b/evidence/box/compare/cand_vs_base_netlist.json` | the w4b commit; `EMCON.md` section 4c; the registry's W4B-D1 to W4B-D3 choices and RF-002 instrument item |
| `w4b/evidence/box/compare/cand_vs_base_schematic.json` | `1dde396ed71e0851d86c65ad8bf684463bd35b78c4edb13786565f220c906894` | 4544 | `fnd/w4b` `drafts/w4b/evidence/box/compare/cand_vs_base_schematic.json` | the w4b commit; `EMCON.md` section 4c; the registry's W4B-D1 to W4B-D3 choices and RF-002 instrument item |
| `w4b/evidence/box/compare/indep_committed_vs_cand.txt` | `d6a6e655f9d15e1937eef03560ccbc9f403dedfa889259210b715fdc08452f28` | 77 | `fnd/w4b` `drafts/w4b/evidence/box/compare/indep_committed_vs_cand.txt` | the w4b commit; `EMCON.md` section 4c; the registry's W4B-D1 to W4B-D3 choices and RF-002 instrument item |
| `w4b/evidence/box/compare/indep_committed_vs_cand_raw.json` | `58c71f05cf24d38b0136f269740b64bc48157e37b30bc560b2524cb3609348ce` | 1719 | `fnd/w4b` `drafts/w4b/evidence/box/compare/indep_committed_vs_cand_raw.json` | the w4b commit; `EMCON.md` section 4c; the registry's W4B-D1 to W4B-D3 choices and RF-002 instrument item |
| `w4b/evidence/box/compare/indep_committed_vs_mainregen.txt` | `ee99fde37c12ab8b10a39b7d5ff246217bd700718ce0681995690328e9cb0eb8` | 188 | `fnd/w4b` `drafts/w4b/evidence/box/compare/indep_committed_vs_mainregen.txt` | the w4b commit; `EMCON.md` section 4c; the registry's W4B-D1 to W4B-D3 choices and RF-002 instrument item |
| `w4b/evidence/box/compare/indep_dropped_W4B-D1_parts_added.txt` | `347ab2c1e188f62668aff4f52d81ed706c295e5ddc8b1d3618ac6c47fa48de35` | 201 | `fnd/w4b` `drafts/w4b/evidence/box/compare/indep_dropped_W4B-D1_parts_added.txt` | the w4b commit; `EMCON.md` section 4c; the registry's W4B-D1 to W4B-D3 choices and RF-002 instrument item |
| `w4b/evidence/box/compare/indep_dropped_W4B-D2_nets_changed.txt` | `03626f4dcfc700e450ad8fb64d5c9506a84b39cc878fc8eb55d4eb9fa0b94b7f` | 254 | `fnd/w4b` `drafts/w4b/evidence/box/compare/indep_dropped_W4B-D2_nets_changed.txt` | the w4b commit; `EMCON.md` section 4c; the registry's W4B-D1 to W4B-D3 choices and RF-002 instrument item |
| `w4b/evidence/box/compare/indep_dropped_W4B-D3_nets_changed.txt` | `2710b7b3b382eecef72ac944c3ccb9cc5d791610be5e90cebb8e6eb05f520662` | 895 | `fnd/w4b` `drafts/w4b/evidence/box/compare/indep_dropped_W4B-D3_nets_changed.txt` | the w4b commit; `EMCON.md` section 4c; the registry's W4B-D1 to W4B-D3 choices and RF-002 instrument item |
| `w4b/evidence/box/compare/indep_dropped_W4B-D3_parts_removed.txt` | `e94f000695bdd0a8ca5084778e5b357c4ec28afb85036beb24c57b28907d5a03` | 176 | `fnd/w4b` `drafts/w4b/evidence/box/compare/indep_dropped_W4B-D3_parts_removed.txt` | the w4b commit; `EMCON.md` section 4c; the registry's W4B-D1 to W4B-D3 choices and RF-002 instrument item |
| `w4b/evidence/box/compare/indep_mainregen_vs_cand.txt` | `d6a6e655f9d15e1937eef03560ccbc9f403dedfa889259210b715fdc08452f28` | 77 | `fnd/w4b` `drafts/w4b/evidence/box/compare/indep_mainregen_vs_cand.txt` | the w4b commit; `EMCON.md` section 4c; the registry's W4B-D1 to W4B-D3 choices and RF-002 instrument item |
| `w4b/evidence/box/incoming.sha256` | `8a5c65df9ad2fb0604b1a16bb46de176159ae36901b0eb4f4f8d0d5fcf4f777a` | 397 | `fnd/w4b` `drafts/w4b/evidence/box/incoming.sha256` | the w4b commit; `EMCON.md` section 4c; the registry's W4B-D1 to W4B-D3 choices and RF-002 instrument item |
| `w4b/evidence/box/prov-after-base.txt` | `49dc87c9fa01343f453df41e2b6a671262d73744a1b484077f8b23a442dc66b6` | 95 | `fnd/w4b` `drafts/w4b/evidence/box/prov-after-base.txt` | the w4b commit; `EMCON.md` section 4c; the registry's W4B-D1 to W4B-D3 choices and RF-002 instrument item |
| `w4b/evidence/box/prov-after-cand.txt` | `2c119f8d819f8b8dff0ab999975eee2cf9dfd03f807b6e0db8f5c2b0dd54ce97` | 95 | `fnd/w4b` `drafts/w4b/evidence/box/prov-after-cand.txt` | the w4b commit; `EMCON.md` section 4c; the registry's W4B-D1 to W4B-D3 choices and RF-002 instrument item |
| `w4b/evidence/box/regen.log` | `d5db7fb2a72f697cd68eac9447381b96c96935dbe121047f2a138d326c63a01b` | 1020 | `fnd/w4b` `drafts/w4b/evidence/box/regen.log` | the w4b commit; `EMCON.md` section 4c; the registry's W4B-D1 to W4B-D3 choices and RF-002 instrument item |
| `w4b/evidence/box/retake-draft.log` | `d9a321cee40f19acb7e053610548e2f91a639d739013ca5c87c7f473335c197f` | 1702 | `fnd/w4b` `drafts/w4b/evidence/box/retake-draft.log` | the w4b commit; `EMCON.md` section 4c; the registry's W4B-D1 to W4B-D3 choices and RF-002 instrument item |
| `w4b/evidence/box/retake.log` | `2031a84677f850bb699f4d0d31243e3cb759b2ea2d0d6f57c0675999f62cad8d` | 1271 | `fnd/w4b` `drafts/w4b/evidence/box/retake.log` | the w4b commit; `EMCON.md` section 4c; the registry's W4B-D1 to W4B-D3 choices and RF-002 instrument item |
| `w4b/evidence/box/setup.log` | `14679fbb17430b9593986e94d377b5694a8c0035e32f1fcc35632146356c123b` | 773 | `fnd/w4b` `drafts/w4b/evidence/box/setup.log` | the w4b commit; `EMCON.md` section 4c; the registry's W4B-D1 to W4B-D3 choices and RF-002 instrument item |
| `w4b/evidence/check_pcb_b/draft-check_cand-netlist.txt` | `d200cca70164ed9189ff43afb9f23de31731f23e7e8e22153a41f1215bf85595` | 5571 | `fnd/w4b` `drafts/w4b/evidence/check_pcb_b/draft-check_cand-netlist.txt` | the w4b commit; `EMCON.md` section 4c; the registry's W4B-D1 to W4B-D3 choices and RF-002 instrument item |
| `w4b/evidence/check_pcb_b/draft-check_main-netlist.txt` | `bf3c07cff2361621d07bc6d64008aacddc7f035ea3cb14300cf3251628e4bc7f` | 5186 | `fnd/w4b` `drafts/w4b/evidence/check_pcb_b/draft-check_main-netlist.txt` | the w4b commit; `EMCON.md` section 4c; the registry's W4B-D1 to W4B-D3 choices and RF-002 instrument item |
| `w4b/evidence/check_pcb_b/main-check_cand-netlist.txt` | `c3087ecc4b3638a88440eb16a22ea258af13e36fd52b4749826c8f9344316a50` | 4512 | `fnd/w4b` `drafts/w4b/evidence/check_pcb_b/main-check_cand-netlist.txt` | the w4b commit; `EMCON.md` section 4c; the registry's W4B-D1 to W4B-D3 choices and RF-002 instrument item |
| `w4b/evidence/check_pcb_b/main-check_main-netlist.txt` | `8795eb2bc7e074eb9353f48336fc6b417c1660f58b361a8a6dd3a3a3e0db6854` | 4527 | `fnd/w4b` `drafts/w4b/evidence/check_pcb_b/main-check_main-netlist.txt` | the w4b commit; `EMCON.md` section 4c; the registry's W4B-D1 to W4B-D3 choices and RF-002 instrument item |
| `w4b/evidence/jlc-query-sn74lv1t08.txt` | `00100f6953b536c9b6bda6ce762f1588e1d820f93afd7c1127c21de1e726b284` | 1122 | `fnd/w4b` `drafts/w4b/evidence/jlc-query-sn74lv1t08.txt` | the w4b commit; `EMCON.md` section 4c; the registry's W4B-D1 to W4B-D3 choices and RF-002 instrument item |
| `w4b/evidence/retake/cand/check_contracts_b.verdict.json` | `0d74eb97381294308a4fa1744be1d740e7f9315d172688a8972a7af738f4970e` | 2438 | `fnd/w4b` `drafts/w4b/evidence/retake/cand/check_contracts_b.verdict.json` | the w4b commit; `EMCON.md` section 4c; the registry's W4B-D1 to W4B-D3 choices and RF-002 instrument item |
| `w4b/evidence/retake/cand/erc_gate.verdict.json` | `e72abcb53fdee160aa1ff76499615fecbceaf29e461550c55fc2cd4fdb049c2c` | 1855 | `fnd/w4b` `drafts/w4b/evidence/retake/cand/erc_gate.verdict.json` | the w4b commit; `EMCON.md` section 4c; the registry's W4B-D1 to W4B-D3 choices and RF-002 instrument item |
| `w4b/evidence/retake/cand/inhibit_chain_a.verdict.json` | `4d3eff32c39834a10de6e670a5d2b29cf1bcbb8e3cc67b8bfaece42afd21b3c9` | 4251 | `fnd/w4b` `drafts/w4b/evidence/retake/cand/inhibit_chain_a.verdict.json` | the w4b commit; `EMCON.md` section 4c; the registry's W4B-D1 to W4B-D3 choices and RF-002 instrument item |
| `w4b/evidence/retake/cand/inhibit_chain_b.verdict.json` | `c59679eb311a3711d256f446a135da2c2d417d9f43061d438bdd7305c3649bb2` | 5371 | `fnd/w4b` `drafts/w4b/evidence/retake/cand/inhibit_chain_b.verdict.json` | the w4b commit; `EMCON.md` section 4c; the registry's W4B-D1 to W4B-D3 choices and RF-002 instrument item |
| `w4b/evidence/retake/cand/inhibit_chain_c.verdict.json` | `3d0e0d0634806527a45ae5e2261a24920fa70d87851de82330739dba51b11c54` | 3783 | `fnd/w4b` `drafts/w4b/evidence/retake/cand/inhibit_chain_c.verdict.json` | the w4b commit; `EMCON.md` section 4c; the registry's W4B-D1 to W4B-D3 choices and RF-002 instrument item |
| `w4b/evidence/retake/cand/inhibit_chain_d.verdict.json` | `a1373df3c146a0c98fcd1a91279a0ec7ed5d0d01018488c2dbcaf24bcd1e5985` | 3498 | `fnd/w4b` `drafts/w4b/evidence/retake/cand/inhibit_chain_d.verdict.json` | the w4b commit; `EMCON.md` section 4c; the registry's W4B-D1 to W4B-D3 choices and RF-002 instrument item |
| `w4b/evidence/retake/cand/inhibit_chain_e.verdict.json` | `8d486de0e402b3673c3be6e176b50c9d0e67307b67e96e4e430f7c97713818f2` | 2901 | `fnd/w4b` `drafts/w4b/evidence/retake/cand/inhibit_chain_e.verdict.json` | the w4b commit; `EMCON.md` section 4c; the registry's W4B-D1 to W4B-D3 choices and RF-002 instrument item |
| `w4b/evidence/retake/cand/inhibit_chain_p.verdict.json` | `d7df266a4f13696b5db32cd176a625b8858daa6f57f471ce15d4e661896f1496` | 2644 | `fnd/w4b` `drafts/w4b/evidence/retake/cand/inhibit_chain_p.verdict.json` | the w4b commit; `EMCON.md` section 4c; the registry's W4B-D1 to W4B-D3 choices and RF-002 instrument item |
| `w4b/evidence/retake/cand/intent_rails.verdict.json` | `44bdb90e84eb19b49485c3feed27b65a4ac0a6cc4c6ade5b37924674f2dd55c3` | 11415 | `fnd/w4b` `drafts/w4b/evidence/retake/cand/intent_rails.verdict.json` | the w4b commit; `EMCON.md` section 4c; the registry's W4B-D1 to W4B-D3 choices and RF-002 instrument item |
| `w4b/evidence/retake/cand/power_sequence.verdict.json` | `8f7dd9b530a7a68b909d1b35867d426a63291f82c99ab8cc4293313fe4c6c066` | 1703 | `fnd/w4b` `drafts/w4b/evidence/retake/cand/power_sequence.verdict.json` | the w4b commit; `EMCON.md` section 4c; the registry's W4B-D1 to W4B-D3 choices and RF-002 instrument item |
| `w4b/evidence/retake/ct/check_contracts_b.verdict.json` | `1c0e6c35aec44457a78658a77bccbe88e32f0201bd8295c2bb4289748a148bdb` | 2438 | `fnd/w4b` `drafts/w4b/evidence/retake/ct/check_contracts_b.verdict.json` | the w4b commit; `EMCON.md` section 4c; the registry's W4B-D1 to W4B-D3 choices and RF-002 instrument item |
| `w4b/evidence/retake/ct/erc_gate.verdict.json` | `691a59152032f642a42049224507527350fc7f5fe5179dd921af58edd0e6c4d7` | 1855 | `fnd/w4b` `drafts/w4b/evidence/retake/ct/erc_gate.verdict.json` | the w4b commit; `EMCON.md` section 4c; the registry's W4B-D1 to W4B-D3 choices and RF-002 instrument item |
| `w4b/evidence/retake/ct/inhibit_chain_a.verdict.json` | `43af509a09608b5c7726eb85a4eec0ddd142c870e983ea31d6b91215f1754ddc` | 3995 | `fnd/w4b` `drafts/w4b/evidence/retake/ct/inhibit_chain_a.verdict.json` | the w4b commit; `EMCON.md` section 4c; the registry's W4B-D1 to W4B-D3 choices and RF-002 instrument item |
| `w4b/evidence/retake/ct/inhibit_chain_b.verdict.json` | `88401362ad94c3475485067a79a708eb024446f6466d93705abccb7e92aae615` | 3953 | `fnd/w4b` `drafts/w4b/evidence/retake/ct/inhibit_chain_b.verdict.json` | the w4b commit; `EMCON.md` section 4c; the registry's W4B-D1 to W4B-D3 choices and RF-002 instrument item |
| `w4b/evidence/retake/ct/inhibit_chain_c.verdict.json` | `837c0f42b6a4ced9de6a11382b1230787d5ac9364ab8852c68e2195c20647a2a` | 3424 | `fnd/w4b` `drafts/w4b/evidence/retake/ct/inhibit_chain_c.verdict.json` | the w4b commit; `EMCON.md` section 4c; the registry's W4B-D1 to W4B-D3 choices and RF-002 instrument item |
| `w4b/evidence/retake/ct/inhibit_chain_d.verdict.json` | `606203d8b8085f04de074b42caa06e597227a472a2f5873a6fe919f97f0e24d0` | 3498 | `fnd/w4b` `drafts/w4b/evidence/retake/ct/inhibit_chain_d.verdict.json` | the w4b commit; `EMCON.md` section 4c; the registry's W4B-D1 to W4B-D3 choices and RF-002 instrument item |
| `w4b/evidence/retake/ct/inhibit_chain_e.verdict.json` | `55fc0f9dc1419b039d31559260b3235b39b5054e78f539a976cc5687936f9b91` | 2901 | `fnd/w4b` `drafts/w4b/evidence/retake/ct/inhibit_chain_e.verdict.json` | the w4b commit; `EMCON.md` section 4c; the registry's W4B-D1 to W4B-D3 choices and RF-002 instrument item |
| `w4b/evidence/retake/ct/inhibit_chain_p.verdict.json` | `2b74e966ac075f2f9f199a5d6b6b22b056283c8f575ee11ad47552292c992b7b` | 2644 | `fnd/w4b` `drafts/w4b/evidence/retake/ct/inhibit_chain_p.verdict.json` | the w4b commit; `EMCON.md` section 4c; the registry's W4B-D1 to W4B-D3 choices and RF-002 instrument item |
| `w4b/evidence/retake/ct/intent_rails.verdict.json` | `8bdd86da22d4a355d3d7dcb12b5d4ad83c588b57b9e3a963d5872544e0f1e3ba` | 11415 | `fnd/w4b` `drafts/w4b/evidence/retake/ct/intent_rails.verdict.json` | the w4b commit; `EMCON.md` section 4c; the registry's W4B-D1 to W4B-D3 choices and RF-002 instrument item |
| `w4b/evidence/retake/ct/power_sequence.verdict.json` | `b7979283090ac3d94332f664246b543b8f2316cbda67ec93118ee95562b32772` | 1703 | `fnd/w4b` `drafts/w4b/evidence/retake/ct/power_sequence.verdict.json` | the w4b commit; `EMCON.md` section 4c; the registry's W4B-D1 to W4B-D3 choices and RF-002 instrument item |
| `w4b/evidence/retake/mt/check_contracts_b.verdict.json` | `45db440f75a180ef87a67af886ae94f7fa8a43c4ae0ea5edc74ce6ae34da2a34` | 2438 | `fnd/w4b` `drafts/w4b/evidence/retake/mt/check_contracts_b.verdict.json` | the w4b commit; `EMCON.md` section 4c; the registry's W4B-D1 to W4B-D3 choices and RF-002 instrument item |
| `w4b/evidence/retake/mt/erc_gate.verdict.json` | `5594014a2978552fbb35ef05003afd4dfdcd27fc7b54a85becba011f8818acb9` | 1855 | `fnd/w4b` `drafts/w4b/evidence/retake/mt/erc_gate.verdict.json` | the w4b commit; `EMCON.md` section 4c; the registry's W4B-D1 to W4B-D3 choices and RF-002 instrument item |
| `w4b/evidence/retake/mt/inhibit_chain_a.verdict.json` | `0eb37a0cb81b09e2de63bb0ff5a65d077e59885b7edb060c21c08b938dce5090` | 3995 | `fnd/w4b` `drafts/w4b/evidence/retake/mt/inhibit_chain_a.verdict.json` | the w4b commit; `EMCON.md` section 4c; the registry's W4B-D1 to W4B-D3 choices and RF-002 instrument item |
| `w4b/evidence/retake/mt/inhibit_chain_b.verdict.json` | `2070b17237ea62bae3c9e1a94a82187889e529ec4714c03c6c132922da6d9ae1` | 4197 | `fnd/w4b` `drafts/w4b/evidence/retake/mt/inhibit_chain_b.verdict.json` | the w4b commit; `EMCON.md` section 4c; the registry's W4B-D1 to W4B-D3 choices and RF-002 instrument item |
| `w4b/evidence/retake/mt/inhibit_chain_c.verdict.json` | `b0e865a3a0bdb29b041e9f99d04413fb620cb833f2bebe8a0e4b653a821887d8` | 3424 | `fnd/w4b` `drafts/w4b/evidence/retake/mt/inhibit_chain_c.verdict.json` | the w4b commit; `EMCON.md` section 4c; the registry's W4B-D1 to W4B-D3 choices and RF-002 instrument item |
| `w4b/evidence/retake/mt/inhibit_chain_d.verdict.json` | `c9529cb9233540ad28248839752bb00380d95b6b554c8e741d03e03587731dd6` | 3498 | `fnd/w4b` `drafts/w4b/evidence/retake/mt/inhibit_chain_d.verdict.json` | the w4b commit; `EMCON.md` section 4c; the registry's W4B-D1 to W4B-D3 choices and RF-002 instrument item |
| `w4b/evidence/retake/mt/inhibit_chain_e.verdict.json` | `b4eb5cd8288789c922415443c6d0fa487089503085cb816e6ff40c61cd7c36b9` | 2901 | `fnd/w4b` `drafts/w4b/evidence/retake/mt/inhibit_chain_e.verdict.json` | the w4b commit; `EMCON.md` section 4c; the registry's W4B-D1 to W4B-D3 choices and RF-002 instrument item |
| `w4b/evidence/retake/mt/inhibit_chain_p.verdict.json` | `299dbbe2de0ad54d29147d1a3fb48434209c0ed839d78fc4f3ea585e8d8e91da` | 2644 | `fnd/w4b` `drafts/w4b/evidence/retake/mt/inhibit_chain_p.verdict.json` | the w4b commit; `EMCON.md` section 4c; the registry's W4B-D1 to W4B-D3 choices and RF-002 instrument item |
| `w4b/evidence/retake/mt/intent_rails.verdict.json` | `7620c3659cf130f0ca98d86df7c003649c6a9cef0dbb81a37f2947eb1e9ae0e7` | 11415 | `fnd/w4b` `drafts/w4b/evidence/retake/mt/intent_rails.verdict.json` | the w4b commit; `EMCON.md` section 4c; the registry's W4B-D1 to W4B-D3 choices and RF-002 instrument item |
| `w4b/evidence/retake/mt/power_sequence.verdict.json` | `e7edd0b07b923de367b21fcdc81ffc5ca3eb8e22cc00eeaa664f2c0bbf6d9ce0` | 1703 | `fnd/w4b` `drafts/w4b/evidence/retake/mt/power_sequence.verdict.json` | the w4b commit; `EMCON.md` section 4c; the registry's W4B-D1 to W4B-D3 choices and RF-002 instrument item |
| `w4b/evidence/retake/retake-cand.err` | `3c39e2904971174c5eb48f7a17b0498729364fb2821e384cd8b5a078121f88d8` | 3538 | `fnd/w4b` `drafts/w4b/evidence/retake/retake-cand.err` | the w4b commit; `EMCON.md` section 4c; the registry's W4B-D1 to W4B-D3 choices and RF-002 instrument item |
| `w4b/evidence/retake/retake-ct.err` | `f4332f0f3e34a53e23304d20ae53549020f6551becc0001f13c91333cc4b78cf` | 3530 | `fnd/w4b` `drafts/w4b/evidence/retake/retake-ct.err` | the w4b commit; `EMCON.md` section 4c; the registry's W4B-D1 to W4B-D3 choices and RF-002 instrument item |
| `w4b/evidence/retake/retake-mt.err` | `62fe18e4603402d573fc11712a13db6fb7f15fc8d268135331548fafc91402e7` | 3530 | `fnd/w4b` `drafts/w4b/evidence/retake/retake-mt.err` | the w4b commit; `EMCON.md` section 4c; the registry's W4B-D1 to W4B-D3 choices and RF-002 instrument item |
| `w4b/evidence/retake/retake-rtb.err` | `22dd52840a15f491f9b0f2a35ca1d9f2d986a79a231ff0025fa127393e586fef` | 3534 | `fnd/w4b` `drafts/w4b/evidence/retake/retake-rtb.err` | the w4b commit; `EMCON.md` section 4c; the registry's W4B-D1 to W4B-D3 choices and RF-002 instrument item |
| `w4b/evidence/retake/rtb/check_contracts_b.verdict.json` | `a486f3ac34b5bf9d2a88bc4415c392fbfd51aa43edf3f913c60c0445f0fcbec4` | 2438 | `fnd/w4b` `drafts/w4b/evidence/retake/rtb/check_contracts_b.verdict.json` | the w4b commit; `EMCON.md` section 4c; the registry's W4B-D1 to W4B-D3 choices and RF-002 instrument item |
| `w4b/evidence/retake/rtb/erc_gate.verdict.json` | `420ecbe9b6b0461f257be8e2c36d1a50c779b459710c7b3d85c3028e37d22fa7` | 1855 | `fnd/w4b` `drafts/w4b/evidence/retake/rtb/erc_gate.verdict.json` | the w4b commit; `EMCON.md` section 4c; the registry's W4B-D1 to W4B-D3 choices and RF-002 instrument item |
| `w4b/evidence/retake/rtb/inhibit_chain_a.verdict.json` | `4826091190db2b353901a53cc67050b46494b638326c2c19767b9e710750795c` | 3995 | `fnd/w4b` `drafts/w4b/evidence/retake/rtb/inhibit_chain_a.verdict.json` | the w4b commit; `EMCON.md` section 4c; the registry's W4B-D1 to W4B-D3 choices and RF-002 instrument item |
| `w4b/evidence/retake/rtb/inhibit_chain_b.verdict.json` | `dfada1c2562cca4df84022a342f230856f80dbb32272edcb0f5a81d5105d09b3` | 4928 | `fnd/w4b` `drafts/w4b/evidence/retake/rtb/inhibit_chain_b.verdict.json` | the w4b commit; `EMCON.md` section 4c; the registry's W4B-D1 to W4B-D3 choices and RF-002 instrument item |
| `w4b/evidence/retake/rtb/inhibit_chain_c.verdict.json` | `492b710b031b27ca486c082dd350240b349f602f217ca634bdf379dc82b9d569` | 3424 | `fnd/w4b` `drafts/w4b/evidence/retake/rtb/inhibit_chain_c.verdict.json` | the w4b commit; `EMCON.md` section 4c; the registry's W4B-D1 to W4B-D3 choices and RF-002 instrument item |
| `w4b/evidence/retake/rtb/inhibit_chain_d.verdict.json` | `4852cebb6b2e687e5fcf21d028552bc5d8c7f3cfe9ccaedca5bfe67718bf6393` | 3498 | `fnd/w4b` `drafts/w4b/evidence/retake/rtb/inhibit_chain_d.verdict.json` | the w4b commit; `EMCON.md` section 4c; the registry's W4B-D1 to W4B-D3 choices and RF-002 instrument item |
| `w4b/evidence/retake/rtb/inhibit_chain_e.verdict.json` | `2285f2963f2d6f06f167b01513994c650957e0494fd5d98196cef98f7d59084e` | 2901 | `fnd/w4b` `drafts/w4b/evidence/retake/rtb/inhibit_chain_e.verdict.json` | the w4b commit; `EMCON.md` section 4c; the registry's W4B-D1 to W4B-D3 choices and RF-002 instrument item |
| `w4b/evidence/retake/rtb/inhibit_chain_p.verdict.json` | `59a96370531c49731d272d2b0c532d47476ec73e024478d63b61b8de0ecf0e50` | 2644 | `fnd/w4b` `drafts/w4b/evidence/retake/rtb/inhibit_chain_p.verdict.json` | the w4b commit; `EMCON.md` section 4c; the registry's W4B-D1 to W4B-D3 choices and RF-002 instrument item |
| `w4b/evidence/retake/rtb/intent_rails.verdict.json` | `5c6c2161275aa31857f6024ccb16ef47b2d31d132afdf836bb06e7e55b299f34` | 11415 | `fnd/w4b` `drafts/w4b/evidence/retake/rtb/intent_rails.verdict.json` | the w4b commit; `EMCON.md` section 4c; the registry's W4B-D1 to W4B-D3 choices and RF-002 instrument item |
| `w4b/evidence/retake/rtb/power_sequence.verdict.json` | `69bfcf28422d5d19bbaae8c1d505d72bf845cd83e4341cb296fbd976a14ae1b0` | 1703 | `fnd/w4b` `drafts/w4b/evidence/retake/rtb/power_sequence.verdict.json` | the w4b commit; `EMCON.md` section 4c; the registry's W4B-D1 to W4B-D3 choices and RF-002 instrument item |
| `w4b/evidence/walk/cand-netlist_draft-tool.txt` | `b1c404b852bc144193dbeb2989e19877efeebb6fbb85c708c5cdcec19382fc0c` | 18038 | `fnd/w4b` `drafts/w4b/evidence/walk/cand-netlist_draft-tool.txt` | the w4b commit; `EMCON.md` section 4c; the registry's W4B-D1 to W4B-D3 choices and RF-002 instrument item |
| `w4b/evidence/walk/cand-netlist_main-tool.txt` | `f5add0d2bf74b500ac0c1c50f6762cb96707ae27a22fe2d849f68ec894882b44` | 19103 | `fnd/w4b` `drafts/w4b/evidence/walk/cand-netlist_main-tool.txt` | the w4b commit; `EMCON.md` section 4c; the registry's W4B-D1 to W4B-D3 choices and RF-002 instrument item |
| `w4b/evidence/walk/main-netlists_draft-tool.txt` | `8c83837163acd826f38f5d9eb474b98b2df2c895d72006621498bb9c697070c7` | 17887 | `fnd/w4b` `drafts/w4b/evidence/walk/main-netlists_draft-tool.txt` | the w4b commit; `EMCON.md` section 4c; the registry's W4B-D1 to W4B-D3 choices and RF-002 instrument item |
| `w4b/evidence/walk/main-netlists_main-tool.txt` | `83e1adaf0b95af918cf62c23ad55ae6b180c03532b06cb862accb24cc83675b9` | 17233 | `fnd/w4b` `drafts/w4b/evidence/walk/main-netlists_main-tool.txt` | the w4b commit; `EMCON.md` section 4c; the registry's W4B-D1 to W4B-D3 choices and RF-002 instrument item |
| `w4b/expected_w4b.json` | `b1370e89b07ada4ca4b1ba3254b4761ff8c32cb97180f9500619af0f7be7a4f5` | 5356 | `fnd/w4b` `drafts/w4b/expected_w4b.json` | the w4b commit; `EMCON.md` section 4c; the registry's W4B-D1 to W4B-D3 choices and RF-002 instrument item |
| `w4b/fixes_w4b_r8int6.py` | `8ad03e0c0accd3f0108ee2593282f248f415e520df4a45a5955f85cc90b012c9` | 8921 | the r8int6 integrator (`fixes_w4b_r8int6.py`) | the w4b commit; `EMCON.md` section 4c; the registry's W4B-D1 to W4B-D3 choices and RF-002 instrument item |
| `w4b/ids_r8int6.json` | `790920a0907ad9d49024a2a1a25add8b93455d4685ba8d732a1a8697405e5ab0` | 92 | the r8int6 integrator (`ids_r8int6.json`) | the w4b commit; `EMCON.md` section 4c; the registry's W4B-D1 to W4B-D3 choices and RF-002 instrument item |
| `w4b/page_drafts_w4b.py` | `f0fe0089c421e1099693a5e1ed79878924474895895a75864927453345356c99` | 23907 | `fnd/w4b` `drafts/w4b/page_drafts_w4b.py` | the w4b commit; `EMCON.md` section 4c; the registry's W4B-D1 to W4B-D3 choices and RF-002 instrument item |
| `w4b/page_drafts_w4b_r8int6.py` | `dee71bfba6c80ec9987d6b3995d2e83cb36b5fb5248696814ec90a4bbea660e5` | 6992 | the r8int6 integrator (`page_drafts_w4b_r8int6.py`) | the w4b commit; `EMCON.md` section 4c; the registry's W4B-D1 to W4B-D3 choices and RF-002 instrument item |
| `w4b/sources-entries.yaml` | `ace0e0804aba3b23aeae9fd46377586b1558d7374c53a1baad1ac80c3f7e0e55` | 3541 | `fnd/w4b` `drafts/w4b/sources-entries.yaml` | the w4b commit; `EMCON.md` section 4c; the registry's W4B-D1 to W4B-D3 choices and RF-002 instrument item |
| `w4b/tools/apply_check_pcb_b_w4b.py` | `35b84ab483e06ff55daf57a4d3a4978b3591ab586ea286e3b19bbcbfd08eab67` | 8904 | `fnd/w4b` `drafts/w4b/tools/apply_check_pcb_b_w4b.py` | the w4b commit; `EMCON.md` section 4c; the registry's W4B-D1 to W4B-D3 choices and RF-002 instrument item |
| `w4b/tools/apply_tx_inhibit_tests_w4b.py` | `a167b6b3df79a894837df60b71768c81f83f237ab136f85397f9160f7b791802` | 4007 | `fnd/w4b` `drafts/w4b/tools/apply_tx_inhibit_tests_w4b.py` | the w4b commit; `EMCON.md` section 4c; the registry's W4B-D1 to W4B-D3 choices and RF-002 instrument item |
| `w4b/tools/apply_tx_inhibit_w4b.py` | `1562e1b36e5a1bb14af529ab489fe9da295f30effd33b36db9dc8d7ed3bf7745` | 10484 | `fnd/w4b` `drafts/w4b/tools/apply_tx_inhibit_w4b.py` | the w4b commit; `EMCON.md` section 4c; the registry's W4B-D1 to W4B-D3 choices and RF-002 instrument item |
| `w4b/tools/emcon_block_harness.py` | `aae3b4e5aa3d8cb6bf357150c8ab451fabc84cd27378367908872cc4b973236f` | 1936 | `fnd/w4b` `drafts/w4b/tools/emcon_block_harness.py` | the w4b commit; `EMCON.md` section 4c; the registry's W4B-D1 to W4B-D3 choices and RF-002 instrument item |
| `w4b/tools/w4b_box.sh` | `bfe3d5261baf9920a715a6db824e4b2ca0b3ca6c0c014e011e05cc2f4b38d50d` | 12745 | `fnd/w4b` `drafts/w4b/tools/w4b_box.sh` | the w4b commit; `EMCON.md` section 4c; the registry's W4B-D1 to W4B-D3 choices and RF-002 instrument item |
| `w4b/w4b-decisions.md` | `9e35b769ddd82e280991d42b7a1877b05c3090ec1c547881ebced6c031160acb` | 16178 | `fnd/w4b` `drafts/w4b/w4b-decisions.md` | the w4b commit; `EMCON.md` section 4c; the registry's W4B-D1 to W4B-D3 choices and RF-002 instrument item |
| `w4c/README.md` | `1f9cec6ea94b2398fc02f472d1cac126b86af253f386e8397836cf24a5c1f099` | 7044 | `fnd/w4c` `drafts/w4c/README.md` | the w4c commit; the registry's EQ-25, PWR-001 and W4C-F1 choices and W4C-F5 item; `EMCON.md` section 4b; EQ-25 |
| `w4c/applied-preview-62f26a44.diff` | `72e7721a34b736a45a3be8c3c27f07795f1d10c3dedbd3b7ea357be8f8e1ddb7` | 157905 | `fnd/w4c` `drafts/w4c/applied-preview-62f26a44.diff` | the w4c commit; the registry's EQ-25, PWR-001 and W4C-F1 choices and W4C-F5 item; `EMCON.md` section 4b; EQ-25 |
| `w4c/applied-preview.diff` | `9bb290fce8464a24cd962ac636bf4aa56b9fb897b04fff773578af4c8a76f67f` | 157380 | `fnd/w4c` `drafts/w4c/applied-preview.diff` | the w4c commit; the registry's EQ-25, PWR-001 and W4C-F1 choices and W4C-F5 item; `EMCON.md` section 4b; EQ-25 |
| `w4c/apply_registry.py` | `30442b62de328da2ca46a8a5b9a807544b1920ff77841cd1c8aa9194a80c2036` | 24862 | `fnd/w4c` `drafts/w4c/apply_registry.py` | the w4c commit; the registry's EQ-25, PWR-001 and W4C-F1 choices and W4C-F5 item; `EMCON.md` section 4b; EQ-25 |
| `w4c/apply_registry_r8int6.py` | `4abf2dbf4b02e1ec756515ed7090d64d86f91e6a13c369ce6f48b6b9fc1cd216` | 26100 | the r8int6 integrator (`apply_registry_r8int6.py`) | the w4c commit; the registry's EQ-25, PWR-001 and W4C-F1 choices and W4C-F5 item; `EMCON.md` section 4b; EQ-25 |
| `w4c/apply_w4c_r8int6.sh` | `fed555594bad9e73714b7c302305afdc0e18b652e07ecb59b5c760992b246b70` | 769 | the r8int6 integrator (`apply_w4c_r8int6.sh`) | the w4c commit; the registry's EQ-25, PWR-001 and W4C-F1 choices and W4C-F5 item; `EMCON.md` section 4b; EQ-25 |
| `w4c/derive_w4c_r8int6.py` | `fc6ca24e493661f6b62c1d012c2890e1a2ee81a9fdb3fa0663a6e71925b156e5` | 9197 | the r8int6 integrator (`derive_w4c_r8int6.py`) | the w4c commit; the registry's EQ-25, PWR-001 and W4C-F1 choices and W4C-F5 item; `EMCON.md` section 4b; EQ-25 |
| `w4c/fixes_w4c_r8int6.py` | `21a7aca0456327f478d4152f40e1cdca92cf433e11ce3b822005d5c9f7ccb2df` | 2564 | the r8int6 integrator (`fixes_w4c_r8int6.py`) | the w4c commit; the registry's EQ-25, PWR-001 and W4C-F1 choices and W4C-F5 item; `EMCON.md` section 4b; EQ-25 |
| `w4c/ids_r8int6.json` | `5211e6712c4748d0486b8058536d56b85b52b4fd08f0fcde6ca67eb2a6337913` | 119 | the r8int6 integrator (`ids_r8int6.json`) | the w4c commit; the registry's EQ-25, PWR-001 and W4C-F1 choices and W4C-F5 item; `EMCON.md` section 4b; EQ-25 |
| `w4c/parity/d_check.sh` | `752c07b16da17edbfd67e668751f78253c59d88d05cc3487778c7d64e9c33c2b` | 702 | `fnd/w4c` `drafts/w4c/parity/d_check.sh` | the w4c commit; the registry's EQ-25, PWR-001 and W4C-F1 choices and W4C-F5 item; `EMCON.md` section 4b; EQ-25 |
| `w4c/parity/expected-c-netlist.json` | `8eeb23b4944cf8a587a75a0a649b0b85c3550889feb2951997ad78f9424fb0b1` | 259 | `fnd/w4c` `drafts/w4c/parity/expected-c-netlist.json` | the w4c commit; the registry's EQ-25, PWR-001 and W4C-F1 choices and W4C-F5 item; `EMCON.md` section 4b; EQ-25 |
| `w4c/parity/expected-empty.json` | `ee7f024913b64242652a6ddcfcbf3763aeeaf8cbc377f50bd9f7be3540885698` | 135 | `fnd/w4c` `drafts/w4c/parity/expected-empty.json` | the w4c commit; the registry's EQ-25, PWR-001 and W4C-F1 choices and W4C-F5 item; `EMCON.md` section 4b; EQ-25 |
| `w4c/parity/fs_levels.py` | `91064660ad6744f5bb41343aebf53173699d813fa276f44dfb6c63bc77942093` | 1487 | `fnd/w4c` `drafts/w4c/parity/fs_levels.py` | the w4c commit; the registry's EQ-25, PWR-001 and W4C-F1 choices and W4C-F5 item; `EMCON.md` section 4b; EQ-25 |
| `w4c/parity/intent-diff.json` | `dc2f48d8adcaccbff455c27fccf6981dfc9a44dd5d23025ddc3585695ae8858b` | 5935 | `fnd/w4c` `drafts/w4c/parity/intent-diff.json` | the w4c commit; the registry's EQ-25, PWR-001 and W4C-F1 choices and W4C-F5 item; `EMCON.md` section 4b; EQ-25 |
| `w4c/parity/netcmp_w4c.py` | `eab4d266765b6a80598d174c083d2b64d146dfdb78ca13f6a8ca226c6c58778b` | 4296 | `fnd/w4c` `drafts/w4c/parity/netcmp_w4c.py` | the w4c commit; the registry's EQ-25, PWR-001 and W4C-F1 choices and W4C-F5 item; `EMCON.md` section 4b; EQ-25 |
| `w4c/parity/p2_pack.sh` | `f348ea5f2d6e590dd7aaa60fa260e5c10fec3a125b18698589e779a14e36e1e5` | 3532 | `fnd/w4c` `drafts/w4c/parity/p2_pack.sh` | the w4c commit; the registry's EQ-25, PWR-001 and W4C-F1 choices and W4C-F5 item; `EMCON.md` section 4b; EQ-25 |
| `w4c/parity/p2_run.sh` | `35d5f55a5d71d89c65eba96c2ba0b8a16dc0ea3372a3f29a2a786b383a719d7a` | 7580 | `fnd/w4c` `drafts/w4c/parity/p2_run.sh` | the w4c commit; the registry's EQ-25, PWR-001 and W4C-F1 choices and W4C-F5 item; `EMCON.md` section 4b; EQ-25 |
| `w4c/parity/regen-candidate-parity_bom.json` | `9f3bd7c28559d84d459c0a2c2b72f092808eca0f17cd6d46f5f464d193a8e44b` | 515 | `fnd/w4c` `drafts/w4c/parity/regen-candidate-parity_bom.json` | the w4c commit; the registry's EQ-25, PWR-001 and W4C-F1 choices and W4C-F5 item; `EMCON.md` section 4b; EQ-25 |
| `w4c/parity/regen-candidate-parity_erc.json` | `b2206f529df747693ef522a86925a45961c80233a99f96726cce0706e01231aa` | 1018 | `fnd/w4c` `drafts/w4c/parity/regen-candidate-parity_erc.json` | the w4c commit; the registry's EQ-25, PWR-001 and W4C-F1 choices and W4C-F5 item; `EMCON.md` section 4b; EQ-25 |
| `w4c/parity/regen-candidate-parity_intent.json` | `86b6a0110a959e0c94dcddd9d79af103dcb184bd4ee78b5403605737b8a18bd6` | 90 | `fnd/w4c` `drafts/w4c/parity/regen-candidate-parity_intent.json` | the w4c commit; the registry's EQ-25, PWR-001 and W4C-F1 choices and W4C-F5 item; `EMCON.md` section 4b; EQ-25 |
| `w4c/parity/regen-candidate-parity_netlist.json` | `8656121eac963da35cb0c3fb31729c51b3b549e7d53038df09afe6a2c4e30ec9` | 5893 | `fnd/w4c` `drafts/w4c/parity/regen-candidate-parity_netlist.json` | the w4c commit; the registry's EQ-25, PWR-001 and W4C-F1 choices and W4C-F5 item; `EMCON.md` section 4b; EQ-25 |
| `w4c/parity/regen-candidate-parity_schematic.json` | `c049e3f004580e8ab64ed23942f1d6d11d0842c2d2a944663708bb0dc7083c9b` | 8931 | `fnd/w4c` `drafts/w4c/parity/regen-candidate-parity_schematic.json` | the w4c commit; the registry's EQ-25, PWR-001 and W4C-F1 choices and W4C-F5 item; `EMCON.md` section 4b; EQ-25 |
| `w4c/parity/regen-candidate.json` | `72aac7eb7a8aacdc811b1aea6c2f8754e512bbf0b9558f76bedd31dd36569a7b` | 3472 | `fnd/w4c` `drafts/w4c/parity/regen-candidate.json` | the w4c commit; the registry's EQ-25, PWR-001 and W4C-F1 choices and W4C-F5 item; `EMCON.md` section 4b; EQ-25 |
| `w4c/parity/regen-main-parity_bom.json` | `0a82344cc1ee2b13316b60a7e397762608aafdd74fe62f099d336407bb50db9e` | 66 | `fnd/w4c` `drafts/w4c/parity/regen-main-parity_bom.json` | the w4c commit; the registry's EQ-25, PWR-001 and W4C-F1 choices and W4C-F5 item; `EMCON.md` section 4b; EQ-25 |
| `w4c/parity/regen-main-parity_erc.json` | `a5e426c995ace7e20521db29284fcea50078ed40ed4da8a8ba8d52913ad3a154` | 353 | `fnd/w4c` `drafts/w4c/parity/regen-main-parity_erc.json` | the w4c commit; the registry's EQ-25, PWR-001 and W4C-F1 choices and W4C-F5 item; `EMCON.md` section 4b; EQ-25 |
| `w4c/parity/regen-main-parity_intent.json` | `607f2e1b7adb75dc66267217a7334114126f37ea6ca8cab0548736b90c1ba3d4` | 76 | `fnd/w4c` `drafts/w4c/parity/regen-main-parity_intent.json` | the w4c commit; the registry's EQ-25, PWR-001 and W4C-F1 choices and W4C-F5 item; `EMCON.md` section 4b; EQ-25 |
| `w4c/parity/regen-main-parity_netlist.json` | `d3699acc140d3afabf3bc245c4ea7c5fa0d296eb73f3fd7406c45ebe88a81e29` | 714 | `fnd/w4c` `drafts/w4c/parity/regen-main-parity_netlist.json` | the w4c commit; the registry's EQ-25, PWR-001 and W4C-F1 choices and W4C-F5 item; `EMCON.md` section 4b; EQ-25 |
| `w4c/parity/regen-main-parity_schematic.json` | `0d8b33fb8dbd84790901f91b70ec3b4afb229de087c6376d8193f0ff4fef10f1` | 359 | `fnd/w4c` `drafts/w4c/parity/regen-main-parity_schematic.json` | the w4c commit; the registry's EQ-25, PWR-001 and W4C-F1 choices and W4C-F5 item; `EMCON.md` section 4b; EQ-25 |
| `w4c/parity/regen-main.json` | `e30d7288bc3dc06557ed2803e0c3a4e286200c1ece4cc1a40b2c183198aec412` | 3488 | `fnd/w4c` `drafts/w4c/parity/regen-main.json` | the w4c commit; the registry's EQ-25, PWR-001 and W4C-F1 choices and W4C-F5 item; `EMCON.md` section 4b; EQ-25 |
| `w4c/parity/rt_table.py` | `2e80746914f5977be7dc3d87c411c0ee050a8fa47df2b45e66418ba48fe80b6d` | 874 | `fnd/w4c` `drafts/w4c/parity/rt_table.py` | the w4c commit; the registry's EQ-25, PWR-001 and W4C-F1 choices and W4C-F5 item; `EMCON.md` section 4b; EQ-25 |
| `w4c/parity/t_run.sh` | `ea60ae670806731fc2bbe5378da749d806b0eb631289176137c71150f462af56` | 2621 | `fnd/w4c` `drafts/w4c/parity/t_run.sh` | the w4c commit; the registry's EQ-25, PWR-001 and W4C-F1 choices and W4C-F5 item; `EMCON.md` section 4b; EQ-25 |
| `w4c/parity/w3a-netcmp-cand.json` | `3959bdec898e799fbfcac5fc60d9eba022d23daf6a7cfca9e7a26967c4cab946` | 1080 | `fnd/w4c` `drafts/w4c/parity/w3a-netcmp-cand.json` | the w4c commit; the registry's EQ-25, PWR-001 and W4C-F1 choices and W4C-F5 item; `EMCON.md` section 4b; EQ-25 |
| `w4c/parity/w4c-parity-cand-vs-pass1.json` | `2ee395deb6a0b62d8f0aa22bba91522120badb98431867744a94de9c0a06e54e` | 519 | `fnd/w4c` `drafts/w4c/parity/w4c-parity-cand-vs-pass1.json` | the w4c commit; the registry's EQ-25, PWR-001 and W4C-F1 choices and W4C-F5 item; `EMCON.md` section 4b; EQ-25 |
| `w4c/parity/w4c-parity-cand.json` | `a1eed19f3499fa777fd4eaffab9b4d2d5ba67df061540954cc5a5041c4e4a480` | 2344 | `fnd/w4c` `drafts/w4c/parity/w4c-parity-cand.json` | the w4c commit; the registry's EQ-25, PWR-001 and W4C-F1 choices and W4C-F5 item; `EMCON.md` section 4b; EQ-25 |
| `w4c/patch_docs.py` | `6a1a9ff34eea553d28a6e49bffa423aace8d69376f688348219776c618893afd` | 27628 | `fnd/w4c` `drafts/w4c/patch_docs.py` | the w4c commit; the registry's EQ-25, PWR-001 and W4C-F1 choices and W4C-F5 item; `EMCON.md` section 4b; EQ-25 |
| `w4c/patch_docs_r8int6.py` | `fc8f33bc65b8b899f3c52d12f852c310a472b9f431a7482756dccc6b62fb14d2` | 30558 | the r8int6 integrator (`patch_docs_r8int6.py`) | the w4c commit; the registry's EQ-25, PWR-001 and W4C-F1 choices and W4C-F5 item; `EMCON.md` section 4b; EQ-25 |
| `w4c/readings/after-candidate/a-check_contracts.verdict.json` | `1ee401e4d0e656647152c36ee70e904aefd862a8c84397fbc33944bd44f3286f` | 2941 | `fnd/w4c` `drafts/w4c/readings/after-candidate/a-check_contracts.verdict.json` | the w4c commit; the registry's EQ-25, PWR-001 and W4C-F1 choices and W4C-F5 item; `EMCON.md` section 4b; EQ-25 |
| `w4c/readings/after-candidate/a-check_contracts_a.verdict.json` | `a6c1dde7f951f0c2516461c465768b32b7847ac091cc47570ac313e4b5110249` | 2693 | `fnd/w4c` `drafts/w4c/readings/after-candidate/a-check_contracts_a.verdict.json` | the w4c commit; the registry's EQ-25, PWR-001 and W4C-F1 choices and W4C-F5 item; `EMCON.md` section 4b; EQ-25 |
| `w4c/readings/after-candidate/a-check_contracts_b.verdict.json` | `22d6411df4aabf0ab12e2ca1cde4f7ba323aca2f2cdd86b30cb220f95eb8726e` | 2438 | `fnd/w4c` `drafts/w4c/readings/after-candidate/a-check_contracts_b.verdict.json` | the w4c commit; the registry's EQ-25, PWR-001 and W4C-F1 choices and W4C-F5 item; `EMCON.md` section 4b; EQ-25 |
| `w4c/readings/after-candidate/a-check_contracts_c.verdict.json` | `e09eb48209c3c06ca53b46894c320d5be37aed86e52232b4e45897032de84b1b` | 2436 | `fnd/w4c` `drafts/w4c/readings/after-candidate/a-check_contracts_c.verdict.json` | the w4c commit; the registry's EQ-25, PWR-001 and W4C-F1 choices and W4C-F5 item; `EMCON.md` section 4b; EQ-25 |
| `w4c/readings/after-candidate/a-check_contracts_d.verdict.json` | `174b3969392d01debe2742d4851a93d8d1c1a30354fc8e3dfdcad1a683565b55` | 2438 | `fnd/w4c` `drafts/w4c/readings/after-candidate/a-check_contracts_d.verdict.json` | the w4c commit; the registry's EQ-25, PWR-001 and W4C-F1 choices and W4C-F5 item; `EMCON.md` section 4b; EQ-25 |
| `w4c/readings/after-candidate/a-check_contracts_e.verdict.json` | `595c931e9fba0cc0a1fcdf89ee1cf4cb4af52652864322a84f9730f17031d3ff` | 2165 | `fnd/w4c` `drafts/w4c/readings/after-candidate/a-check_contracts_e.verdict.json` | the w4c commit; the registry's EQ-25, PWR-001 and W4C-F1 choices and W4C-F5 item; `EMCON.md` section 4b; EQ-25 |
| `w4c/readings/after-candidate/a-check_contracts_p.verdict.json` | `8056c0f17a3cd0438964cd43197b8d395fb9fee6c3ac1b8f65df30bef7544ecb` | 1906 | `fnd/w4c` `drafts/w4c/readings/after-candidate/a-check_contracts_p.verdict.json` | the w4c commit; the registry's EQ-25, PWR-001 and W4C-F1 choices and W4C-F5 item; `EMCON.md` section 4b; EQ-25 |
| `w4c/readings/after-candidate/a-clock_check.verdict.json` | `c6ab85ecf5e73aa966ff105fa8876a2449927ac2c06817f25ec808ac89c403a8` | 1076 | `fnd/w4c` `drafts/w4c/readings/after-candidate/a-clock_check.verdict.json` | the w4c commit; the registry's EQ-25, PWR-001 and W4C-F1 choices and W4C-F5 item; `EMCON.md` section 4b; EQ-25 |
| `w4c/readings/after-candidate/a-derate.verdict.json` | `d6c9c21211b7a66424e53bf32e3e0b43aacdf2c2ea082dc85621496da0703cdc` | 1254 | `fnd/w4c` `drafts/w4c/readings/after-candidate/a-derate.verdict.json` | the w4c commit; the registry's EQ-25, PWR-001 and W4C-F1 choices and W4C-F5 item; `EMCON.md` section 4b; EQ-25 |
| `w4c/readings/after-candidate/a-edge_length.verdict.json` | `77be9e3f6aa98d543c6c179d94b048645f272769abc41e34de2803f167fafc68` | 9116 | `fnd/w4c` `drafts/w4c/readings/after-candidate/a-edge_length.verdict.json` | the w4c commit; the registry's EQ-25, PWR-001 and W4C-F1 choices and W4C-F5 item; `EMCON.md` section 4b; EQ-25 |
| `w4c/readings/after-candidate/a-energy_chain.verdict.json` | `c5745853927a5c6bd3c908e91afbdbcb75f9b893a486e42ace165cf579961f3c` | 2479 | `fnd/w4c` `drafts/w4c/readings/after-candidate/a-energy_chain.verdict.json` | the w4c commit; the registry's EQ-25, PWR-001 and W4C-F1 choices and W4C-F5 item; `EMCON.md` section 4b; EQ-25 |
| `w4c/readings/after-candidate/a-energy_chain_a.verdict.json` | `23a79b47ab972929f82a47e96a3afbf1e7fecadfcf4eea799d968dcb1be1ac02` | 1750 | `fnd/w4c` `drafts/w4c/readings/after-candidate/a-energy_chain_a.verdict.json` | the w4c commit; the registry's EQ-25, PWR-001 and W4C-F1 choices and W4C-F5 item; `EMCON.md` section 4b; EQ-25 |
| `w4c/readings/after-candidate/a-energy_chain_b.verdict.json` | `6c1e877538c8c2207df181dd6e7067000c4191b9be26536848327ced71534697` | 1612 | `fnd/w4c` `drafts/w4c/readings/after-candidate/a-energy_chain_b.verdict.json` | the w4c commit; the registry's EQ-25, PWR-001 and W4C-F1 choices and W4C-F5 item; `EMCON.md` section 4b; EQ-25 |
| `w4c/readings/after-candidate/a-energy_chain_e.verdict.json` | `e8752f616a1dac8c83efd0cd85cb28a6c762551b8a49dc61c8c4453339d38df0` | 1750 | `fnd/w4c` `drafts/w4c/readings/after-candidate/a-energy_chain_e.verdict.json` | the w4c commit; the registry's EQ-25, PWR-001 and W4C-F1 choices and W4C-F5 item; `EMCON.md` section 4b; EQ-25 |
| `w4c/readings/after-candidate/a-energy_chain_e5.verdict.json` | `8b4f8777899799020c1f93c036ae03f7cac03e0199a427dcd1c9c1025d4db4a7` | 1558 | `fnd/w4c` `drafts/w4c/readings/after-candidate/a-energy_chain_e5.verdict.json` | the w4c commit; the registry's EQ-25, PWR-001 and W4C-F1 choices and W4C-F5 item; `EMCON.md` section 4b; EQ-25 |
| `w4c/readings/after-candidate/a-energy_chain_p.verdict.json` | `58836ebc26ad12a6ed9fb96a4f5be37012b1e05896a820312020a25202efa53b` | 1606 | `fnd/w4c` `drafts/w4c/readings/after-candidate/a-energy_chain_p.verdict.json` | the w4c commit; the registry's EQ-25, PWR-001 and W4C-F1 choices and W4C-F5 item; `EMCON.md` section 4b; EQ-25 |
| `w4c/readings/after-candidate/a-erc_gate.verdict.json` | `7eabeb1f4ce56b94efd45fc9d993b3fee7bea572ee2421963d51137093f8a924` | 1724 | `fnd/w4c` `drafts/w4c/readings/after-candidate/a-erc_gate.verdict.json` | the w4c commit; the registry's EQ-25, PWR-001 and W4C-F1 choices and W4C-F5 item; `EMCON.md` section 4b; EQ-25 |
| `w4c/readings/after-candidate/a-inhibit_chain_a.verdict.json` | `ddff9968f1bf26885562adcfe10343f495ac86983c50124223d19d80f5b5cf2d` | 3754 | `fnd/w4c` `drafts/w4c/readings/after-candidate/a-inhibit_chain_a.verdict.json` | the w4c commit; the registry's EQ-25, PWR-001 and W4C-F1 choices and W4C-F5 item; `EMCON.md` section 4b; EQ-25 |
| `w4c/readings/after-candidate/a-inhibit_chain_b.verdict.json` | `c27236589c3403b8cffd5c16f342702037e457325ba29ebcccc3cf6b8ee632c3` | 4679 | `fnd/w4c` `drafts/w4c/readings/after-candidate/a-inhibit_chain_b.verdict.json` | the w4c commit; the registry's EQ-25, PWR-001 and W4C-F1 choices and W4C-F5 item; `EMCON.md` section 4b; EQ-25 |
| `w4c/readings/after-candidate/a-inhibit_chain_c.verdict.json` | `1c8fa0dda51da3b00bedf140a718bbf01f4badc37d90a4ede8af24ca8a6b88ec` | 3174 | `fnd/w4c` `drafts/w4c/readings/after-candidate/a-inhibit_chain_c.verdict.json` | the w4c commit; the registry's EQ-25, PWR-001 and W4C-F1 choices and W4C-F5 item; `EMCON.md` section 4b; EQ-25 |
| `w4c/readings/after-candidate/a-inhibit_chain_d.verdict.json` | `d0290df0b97c1ca5ecc5372720fa216f2e3f8e2210850163cc554ff36569957c` | 3371 | `fnd/w4c` `drafts/w4c/readings/after-candidate/a-inhibit_chain_d.verdict.json` | the w4c commit; the registry's EQ-25, PWR-001 and W4C-F1 choices and W4C-F5 item; `EMCON.md` section 4b; EQ-25 |
| `w4c/readings/after-candidate/a-inhibit_chain_e.verdict.json` | `2f770b5363097eafb8931175fccaab5a8815fa6547e7b091d5fb0f76f67bc694` | 2901 | `fnd/w4c` `drafts/w4c/readings/after-candidate/a-inhibit_chain_e.verdict.json` | the w4c commit; the registry's EQ-25, PWR-001 and W4C-F1 choices and W4C-F5 item; `EMCON.md` section 4b; EQ-25 |
| `w4c/readings/after-candidate/a-inhibit_chain_p.verdict.json` | `4475a69340f9cd2d41ae226cd65ea0981e9c1fcd13474af0537cab09969a8aa2` | 2644 | `fnd/w4c` `drafts/w4c/readings/after-candidate/a-inhibit_chain_p.verdict.json` | the w4c commit; the registry's EQ-25, PWR-001 and W4C-F1 choices and W4C-F5 item; `EMCON.md` section 4b; EQ-25 |
| `w4c/readings/after-candidate/a-intent_rails.verdict.json` | `2bd287d91f4a890bad39022dc30fbb0b5cab9482efab86af9750b2246eac413e` | 11046 | `fnd/w4c` `drafts/w4c/readings/after-candidate/a-intent_rails.verdict.json` | the w4c commit; the registry's EQ-25, PWR-001 and W4C-F1 choices and W4C-F5 item; `EMCON.md` section 4b; EQ-25 |
| `w4c/readings/after-candidate/a-interfaces.verdict.json` | `62dcb941b0876f869b2fe1b463fd4083b984d5e28fb08b48bceaf8111b345d41` | 1458 | `fnd/w4c` `drafts/w4c/readings/after-candidate/a-interfaces.verdict.json` | the w4c commit; the registry's EQ-25, PWR-001 and W4C-F1 choices and W4C-F5 item; `EMCON.md` section 4b; EQ-25 |
| `w4c/readings/after-candidate/a-interfaces_a.verdict.json` | `07d8b77661ce077b03148029e426b867e1f084d9b90d3a189860e13a977ad390` | 1627 | `fnd/w4c` `drafts/w4c/readings/after-candidate/a-interfaces_a.verdict.json` | the w4c commit; the registry's EQ-25, PWR-001 and W4C-F1 choices and W4C-F5 item; `EMCON.md` section 4b; EQ-25 |
| `w4c/readings/after-candidate/a-interfaces_b.verdict.json` | `e11d76ed339aaa560aec9bcc0b87794897cc39b3ff03df91224999abfc181394` | 1635 | `fnd/w4c` `drafts/w4c/readings/after-candidate/a-interfaces_b.verdict.json` | the w4c commit; the registry's EQ-25, PWR-001 and W4C-F1 choices and W4C-F5 item; `EMCON.md` section 4b; EQ-25 |
| `w4c/readings/after-candidate/a-interfaces_c.verdict.json` | `48690406e99a18546bf6470d29168223c22d6802b2036464dc5e4278c66e40b6` | 1633 | `fnd/w4c` `drafts/w4c/readings/after-candidate/a-interfaces_c.verdict.json` | the w4c commit; the registry's EQ-25, PWR-001 and W4C-F1 choices and W4C-F5 item; `EMCON.md` section 4b; EQ-25 |
| `w4c/readings/after-candidate/a-interfaces_d.verdict.json` | `33040840f72681981c68d429513b6f8673d07d57717ef6822ce1f8ebabc128bf` | 1621 | `fnd/w4c` `drafts/w4c/readings/after-candidate/a-interfaces_d.verdict.json` | the w4c commit; the registry's EQ-25, PWR-001 and W4C-F1 choices and W4C-F5 item; `EMCON.md` section 4b; EQ-25 |
| `w4c/readings/after-candidate/a-interfaces_e.verdict.json` | `cc2597a6e55619fe0d0438d32e8b22ecdba6ea70d1039b3800d4311328f6e63c` | 1625 | `fnd/w4c` `drafts/w4c/readings/after-candidate/a-interfaces_e.verdict.json` | the w4c commit; the registry's EQ-25, PWR-001 and W4C-F1 choices and W4C-F5 item; `EMCON.md` section 4b; EQ-25 |
| `w4c/readings/after-candidate/a-interfaces_e5.verdict.json` | `ad9ce2634c67ed30879cbcf0948dfe9423bbade4ae5f2021f811c33af4c594f1` | 1802 | `fnd/w4c` `drafts/w4c/readings/after-candidate/a-interfaces_e5.verdict.json` | the w4c commit; the registry's EQ-25, PWR-001 and W4C-F1 choices and W4C-F5 item; `EMCON.md` section 4b; EQ-25 |
| `w4c/readings/after-candidate/a-interfaces_p.verdict.json` | `5f5c397ff56973fc59103e50554a244cfb1555c9bdbf0716491c5cd82ac26d7a` | 1621 | `fnd/w4c` `drafts/w4c/readings/after-candidate/a-interfaces_p.verdict.json` | the w4c commit; the registry's EQ-25, PWR-001 and W4C-F1 choices and W4C-F5 item; `EMCON.md` section 4b; EQ-25 |
| `w4c/readings/after-candidate/a-pin_map_lands_a.verdict.json` | `e4a4c043c9f22f1553f65485ca94eea893c18669b1491f63351490e9c0d97e49` | 1250 | `fnd/w4c` `drafts/w4c/readings/after-candidate/a-pin_map_lands_a.verdict.json` | the w4c commit; the registry's EQ-25, PWR-001 and W4C-F1 choices and W4C-F5 item; `EMCON.md` section 4b; EQ-25 |
| `w4c/readings/after-candidate/a-port_protect.verdict.json` | `9e05780da64fd9f67dcf78da8d4330fcb8d1286487eeb7bda6b6a551f8b5f4b8` | 1679 | `fnd/w4c` `drafts/w4c/readings/after-candidate/a-port_protect.verdict.json` | the w4c commit; the registry's EQ-25, PWR-001 and W4C-F1 choices and W4C-F5 item; `EMCON.md` section 4b; EQ-25 |
| `w4c/readings/after-candidate/a-port_protect_a.verdict.json` | `ba352aceed703d9d135b430c36cedc88a4698b617a68089eab7544314e9fab94` | 1758 | `fnd/w4c` `drafts/w4c/readings/after-candidate/a-port_protect_a.verdict.json` | the w4c commit; the registry's EQ-25, PWR-001 and W4C-F1 choices and W4C-F5 item; `EMCON.md` section 4b; EQ-25 |
| `w4c/readings/after-candidate/a-power_sequence.verdict.json` | `9b86ffbbf60678a2519eef9677828c4302e9cb90d5104304b01b536ef8ec0f3c` | 1698 | `fnd/w4c` `drafts/w4c/readings/after-candidate/a-power_sequence.verdict.json` | the w4c commit; the registry's EQ-25, PWR-001 and W4C-F1 choices and W4C-F5 item; `EMCON.md` section 4b; EQ-25 |
| `w4c/readings/after-candidate/a-safe_lines.verdict.json` | `01a08aab16d26a43055c23e8a5a81ee115e5558e9394da9de6f72307087c5523` | 2581 | `fnd/w4c` `drafts/w4c/readings/after-candidate/a-safe_lines.verdict.json` | the w4c commit; the registry's EQ-25, PWR-001 and W4C-F1 choices and W4C-F5 item; `EMCON.md` section 4b; EQ-25 |
| `w4c/readings/after-candidate/a-safe_lines_a.verdict.json` | `4a7bd968c7039fadeb33c9f4ba9126a6690295e8031a0ed2f25bb9053eaab8da` | 2583 | `fnd/w4c` `drafts/w4c/readings/after-candidate/a-safe_lines_a.verdict.json` | the w4c commit; the registry's EQ-25, PWR-001 and W4C-F1 choices and W4C-F5 item; `EMCON.md` section 4b; EQ-25 |
| `w4c/readings/after-candidate/b-check_contracts.verdict.json` | `83ad155f7619083638f858bbbad2d93b246a2adc7f09673b6dadc29ed5a7ce7d` | 2941 | `fnd/w4c` `drafts/w4c/readings/after-candidate/b-check_contracts.verdict.json` | the w4c commit; the registry's EQ-25, PWR-001 and W4C-F1 choices and W4C-F5 item; `EMCON.md` section 4b; EQ-25 |
| `w4c/readings/after-candidate/b-check_contracts_a.verdict.json` | `c0a0783ba7b8401f415bcc6fe67990c23a9803334d56d19996ca95cb1085fa47` | 2693 | `fnd/w4c` `drafts/w4c/readings/after-candidate/b-check_contracts_a.verdict.json` | the w4c commit; the registry's EQ-25, PWR-001 and W4C-F1 choices and W4C-F5 item; `EMCON.md` section 4b; EQ-25 |
| `w4c/readings/after-candidate/b-check_contracts_b.verdict.json` | `5973bba632d27d2c4f5561dea57a08c5caebe66f06811c3a79471ebf74065585` | 2438 | `fnd/w4c` `drafts/w4c/readings/after-candidate/b-check_contracts_b.verdict.json` | the w4c commit; the registry's EQ-25, PWR-001 and W4C-F1 choices and W4C-F5 item; `EMCON.md` section 4b; EQ-25 |
| `w4c/readings/after-candidate/b-check_contracts_c.verdict.json` | `d42017b22835209471e1793d1f3309d4994b2f024b63806a340153f61f4c957e` | 2436 | `fnd/w4c` `drafts/w4c/readings/after-candidate/b-check_contracts_c.verdict.json` | the w4c commit; the registry's EQ-25, PWR-001 and W4C-F1 choices and W4C-F5 item; `EMCON.md` section 4b; EQ-25 |
| `w4c/readings/after-candidate/b-check_contracts_d.verdict.json` | `bc63b18764ca2b862ecdcee379d5bc346c436e009448a5c085c37f45e4d3794c` | 2438 | `fnd/w4c` `drafts/w4c/readings/after-candidate/b-check_contracts_d.verdict.json` | the w4c commit; the registry's EQ-25, PWR-001 and W4C-F1 choices and W4C-F5 item; `EMCON.md` section 4b; EQ-25 |
| `w4c/readings/after-candidate/b-check_contracts_e.verdict.json` | `d31370be4a10298cb8586840229551d58287415d309084058532805b297698dc` | 2165 | `fnd/w4c` `drafts/w4c/readings/after-candidate/b-check_contracts_e.verdict.json` | the w4c commit; the registry's EQ-25, PWR-001 and W4C-F1 choices and W4C-F5 item; `EMCON.md` section 4b; EQ-25 |
| `w4c/readings/after-candidate/b-check_contracts_p.verdict.json` | `fbb7561a548edc7a04e6bfa2bd95b9728e93f8d70a394d2ea9291a876bce33b0` | 1906 | `fnd/w4c` `drafts/w4c/readings/after-candidate/b-check_contracts_p.verdict.json` | the w4c commit; the registry's EQ-25, PWR-001 and W4C-F1 choices and W4C-F5 item; `EMCON.md` section 4b; EQ-25 |
| `w4c/readings/after-candidate/b-clock_check.verdict.json` | `98a1f41eb90861a06d65f5d779574c09135dcd12d3e6be23a4260fb9484a1369` | 1221 | `fnd/w4c` `drafts/w4c/readings/after-candidate/b-clock_check.verdict.json` | the w4c commit; the registry's EQ-25, PWR-001 and W4C-F1 choices and W4C-F5 item; `EMCON.md` section 4b; EQ-25 |
| `w4c/readings/after-candidate/b-derate.verdict.json` | `c889847333274b8bf3db8973f92b640b2c96c916259be8db92e25c1067f0081a` | 1256 | `fnd/w4c` `drafts/w4c/readings/after-candidate/b-derate.verdict.json` | the w4c commit; the registry's EQ-25, PWR-001 and W4C-F1 choices and W4C-F5 item; `EMCON.md` section 4b; EQ-25 |
| `w4c/readings/after-candidate/b-edge_length.verdict.json` | `ae6c581ebb94100b271cb8caf64e2e66bfb196a153d72f75871746a6c8e70fa4` | 27360 | `fnd/w4c` `drafts/w4c/readings/after-candidate/b-edge_length.verdict.json` | the w4c commit; the registry's EQ-25, PWR-001 and W4C-F1 choices and W4C-F5 item; `EMCON.md` section 4b; EQ-25 |
| `w4c/readings/after-candidate/b-energy_chain.verdict.json` | `dbd3ce133d1b4d5a7da23db5629ccf5a5089a77b67e648c2bbfe83292a4fb814` | 2479 | `fnd/w4c` `drafts/w4c/readings/after-candidate/b-energy_chain.verdict.json` | the w4c commit; the registry's EQ-25, PWR-001 and W4C-F1 choices and W4C-F5 item; `EMCON.md` section 4b; EQ-25 |
| `w4c/readings/after-candidate/b-energy_chain_a.verdict.json` | `f7823b175cf38cd46f6742f23837e9e3b2dc21172507142b242e0078b28da20c` | 1750 | `fnd/w4c` `drafts/w4c/readings/after-candidate/b-energy_chain_a.verdict.json` | the w4c commit; the registry's EQ-25, PWR-001 and W4C-F1 choices and W4C-F5 item; `EMCON.md` section 4b; EQ-25 |
| `w4c/readings/after-candidate/b-energy_chain_b.verdict.json` | `1251df56795bbbbe657053fa6ca0a8159ad788d8ba394d19c538c452badd9e51` | 1612 | `fnd/w4c` `drafts/w4c/readings/after-candidate/b-energy_chain_b.verdict.json` | the w4c commit; the registry's EQ-25, PWR-001 and W4C-F1 choices and W4C-F5 item; `EMCON.md` section 4b; EQ-25 |
| `w4c/readings/after-candidate/b-energy_chain_e.verdict.json` | `4a35bbade758f448717050c7ef50ef99fb58f76d2606c0b2a1dd08e3b27a77fc` | 1750 | `fnd/w4c` `drafts/w4c/readings/after-candidate/b-energy_chain_e.verdict.json` | the w4c commit; the registry's EQ-25, PWR-001 and W4C-F1 choices and W4C-F5 item; `EMCON.md` section 4b; EQ-25 |
| `w4c/readings/after-candidate/b-energy_chain_e5.verdict.json` | `0f8655d90114a89dcfe8bfdc216bfe4e75a0ef0111dfa6a735327d4c1cc5d5d4` | 1558 | `fnd/w4c` `drafts/w4c/readings/after-candidate/b-energy_chain_e5.verdict.json` | the w4c commit; the registry's EQ-25, PWR-001 and W4C-F1 choices and W4C-F5 item; `EMCON.md` section 4b; EQ-25 |
| `w4c/readings/after-candidate/b-energy_chain_p.verdict.json` | `0a41f9fc8e35820fedac7e5f873489258cea873e1831bf740ba191a1846e1b98` | 1606 | `fnd/w4c` `drafts/w4c/readings/after-candidate/b-energy_chain_p.verdict.json` | the w4c commit; the registry's EQ-25, PWR-001 and W4C-F1 choices and W4C-F5 item; `EMCON.md` section 4b; EQ-25 |
| `w4c/readings/after-candidate/b-erc_gate.verdict.json` | `6a7fc88b26f0f00e206ebf432792679d9d3516f66b5931458eaae876cf77eeda` | 1855 | `fnd/w4c` `drafts/w4c/readings/after-candidate/b-erc_gate.verdict.json` | the w4c commit; the registry's EQ-25, PWR-001 and W4C-F1 choices and W4C-F5 item; `EMCON.md` section 4b; EQ-25 |
| `w4c/readings/after-candidate/b-inhibit_chain_a.verdict.json` | `e4e9dbc50a5e3d6baba6da6b8d5c2ef34b4ca0ae5c03cb334cb6f61ee003b168` | 3754 | `fnd/w4c` `drafts/w4c/readings/after-candidate/b-inhibit_chain_a.verdict.json` | the w4c commit; the registry's EQ-25, PWR-001 and W4C-F1 choices and W4C-F5 item; `EMCON.md` section 4b; EQ-25 |
| `w4c/readings/after-candidate/b-inhibit_chain_b.verdict.json` | `df771c8212bf9812408b1d615abcd749eb239b2c89d7075823f3b57a38648bb9` | 4679 | `fnd/w4c` `drafts/w4c/readings/after-candidate/b-inhibit_chain_b.verdict.json` | the w4c commit; the registry's EQ-25, PWR-001 and W4C-F1 choices and W4C-F5 item; `EMCON.md` section 4b; EQ-25 |
| `w4c/readings/after-candidate/b-inhibit_chain_c.verdict.json` | `e63fa841d92510f9dfd1a79d248b19b0f2b119b82024ca3484f70c89dcfc3fef` | 3174 | `fnd/w4c` `drafts/w4c/readings/after-candidate/b-inhibit_chain_c.verdict.json` | the w4c commit; the registry's EQ-25, PWR-001 and W4C-F1 choices and W4C-F5 item; `EMCON.md` section 4b; EQ-25 |
| `w4c/readings/after-candidate/b-inhibit_chain_d.verdict.json` | `6af87c8fa6eccb4a42c767f194958a8a7ce84feefb3e7b470eb4119489737390` | 3371 | `fnd/w4c` `drafts/w4c/readings/after-candidate/b-inhibit_chain_d.verdict.json` | the w4c commit; the registry's EQ-25, PWR-001 and W4C-F1 choices and W4C-F5 item; `EMCON.md` section 4b; EQ-25 |
| `w4c/readings/after-candidate/b-inhibit_chain_e.verdict.json` | `bfb668ace2e6f299c04e769a2e1426ae2f1c948d4adf212d5ba73d13011bebab` | 2901 | `fnd/w4c` `drafts/w4c/readings/after-candidate/b-inhibit_chain_e.verdict.json` | the w4c commit; the registry's EQ-25, PWR-001 and W4C-F1 choices and W4C-F5 item; `EMCON.md` section 4b; EQ-25 |
| `w4c/readings/after-candidate/b-inhibit_chain_p.verdict.json` | `996109eb1d10b16449540e3ce41b8a7284e7158024c9589707cd05be7cdf38a3` | 2644 | `fnd/w4c` `drafts/w4c/readings/after-candidate/b-inhibit_chain_p.verdict.json` | the w4c commit; the registry's EQ-25, PWR-001 and W4C-F1 choices and W4C-F5 item; `EMCON.md` section 4b; EQ-25 |
| `w4c/readings/after-candidate/b-intent_rails.verdict.json` | `9e7b819e40814f8944201794fec6e194decbdf2fc129a8fc05cfbbb2fabab0b2` | 11415 | `fnd/w4c` `drafts/w4c/readings/after-candidate/b-intent_rails.verdict.json` | the w4c commit; the registry's EQ-25, PWR-001 and W4C-F1 choices and W4C-F5 item; `EMCON.md` section 4b; EQ-25 |
| `w4c/readings/after-candidate/b-interfaces.verdict.json` | `376f6d195f4d15d6526b817fe513ffe55e1faa40859fb54d8f841b186d5ed3d7` | 1458 | `fnd/w4c` `drafts/w4c/readings/after-candidate/b-interfaces.verdict.json` | the w4c commit; the registry's EQ-25, PWR-001 and W4C-F1 choices and W4C-F5 item; `EMCON.md` section 4b; EQ-25 |
| `w4c/readings/after-candidate/b-interfaces_a.verdict.json` | `7ce82450cf23de70597927d5dc4d18ccd6ab1e7a27a6b8bc0e1e22c936139309` | 1627 | `fnd/w4c` `drafts/w4c/readings/after-candidate/b-interfaces_a.verdict.json` | the w4c commit; the registry's EQ-25, PWR-001 and W4C-F1 choices and W4C-F5 item; `EMCON.md` section 4b; EQ-25 |
| `w4c/readings/after-candidate/b-interfaces_b.verdict.json` | `5cf54f5617981192a708ec5606c086976dc409c8e5171e26abcd660ec4804791` | 1635 | `fnd/w4c` `drafts/w4c/readings/after-candidate/b-interfaces_b.verdict.json` | the w4c commit; the registry's EQ-25, PWR-001 and W4C-F1 choices and W4C-F5 item; `EMCON.md` section 4b; EQ-25 |
| `w4c/readings/after-candidate/b-interfaces_c.verdict.json` | `6741c68cecaff2476ac3121994f5038e52d717e5f018d59171d3902888fb6372` | 1633 | `fnd/w4c` `drafts/w4c/readings/after-candidate/b-interfaces_c.verdict.json` | the w4c commit; the registry's EQ-25, PWR-001 and W4C-F1 choices and W4C-F5 item; `EMCON.md` section 4b; EQ-25 |
| `w4c/readings/after-candidate/b-interfaces_d.verdict.json` | `ef563856a24fde78e0990a14df2e960991cfeb35f87d8441f30a81d1d6466e9d` | 1621 | `fnd/w4c` `drafts/w4c/readings/after-candidate/b-interfaces_d.verdict.json` | the w4c commit; the registry's EQ-25, PWR-001 and W4C-F1 choices and W4C-F5 item; `EMCON.md` section 4b; EQ-25 |
| `w4c/readings/after-candidate/b-interfaces_e.verdict.json` | `f1631745c51033c8598aacc9e48c3f32e56ab179700905195ca095970a1b6bbb` | 1625 | `fnd/w4c` `drafts/w4c/readings/after-candidate/b-interfaces_e.verdict.json` | the w4c commit; the registry's EQ-25, PWR-001 and W4C-F1 choices and W4C-F5 item; `EMCON.md` section 4b; EQ-25 |
| `w4c/readings/after-candidate/b-interfaces_e5.verdict.json` | `0d347716075388ba9f964f6d855d652846ed2bf95ed669ae6c086066a5e7637e` | 1802 | `fnd/w4c` `drafts/w4c/readings/after-candidate/b-interfaces_e5.verdict.json` | the w4c commit; the registry's EQ-25, PWR-001 and W4C-F1 choices and W4C-F5 item; `EMCON.md` section 4b; EQ-25 |
| `w4c/readings/after-candidate/b-interfaces_p.verdict.json` | `d9857c658fabde386d0617c2a5d938e6fa61b6980eb9234ab8609867ddcdd1a7` | 1621 | `fnd/w4c` `drafts/w4c/readings/after-candidate/b-interfaces_p.verdict.json` | the w4c commit; the registry's EQ-25, PWR-001 and W4C-F1 choices and W4C-F5 item; `EMCON.md` section 4b; EQ-25 |
| `w4c/readings/after-candidate/b-pin_map_lands_b.verdict.json` | `6e41aee37cac9a7790b87b6cf4968bfcf513a0379cd0bf33e344a12f79636518` | 1254 | `fnd/w4c` `drafts/w4c/readings/after-candidate/b-pin_map_lands_b.verdict.json` | the w4c commit; the registry's EQ-25, PWR-001 and W4C-F1 choices and W4C-F5 item; `EMCON.md` section 4b; EQ-25 |
| `w4c/readings/after-candidate/b-port_protect.verdict.json` | `af5ad6bfc12e27b53379cf744bf20e640dfd939345f6e494f08e572455c803ac` | 1683 | `fnd/w4c` `drafts/w4c/readings/after-candidate/b-port_protect.verdict.json` | the w4c commit; the registry's EQ-25, PWR-001 and W4C-F1 choices and W4C-F5 item; `EMCON.md` section 4b; EQ-25 |
| `w4c/readings/after-candidate/b-port_protect_b.verdict.json` | `9329615cdb88d5107c83e1b1e6a0d8cbdb83ba97e12f72052d9645725a5fb4ec` | 1762 | `fnd/w4c` `drafts/w4c/readings/after-candidate/b-port_protect_b.verdict.json` | the w4c commit; the registry's EQ-25, PWR-001 and W4C-F1 choices and W4C-F5 item; `EMCON.md` section 4b; EQ-25 |
| `w4c/readings/after-candidate/b-power_sequence.verdict.json` | `f0f0ac9e4e26361dcb844ac19668414ca3a84d22077e6258149dced1efbdd79d` | 1703 | `fnd/w4c` `drafts/w4c/readings/after-candidate/b-power_sequence.verdict.json` | the w4c commit; the registry's EQ-25, PWR-001 and W4C-F1 choices and W4C-F5 item; `EMCON.md` section 4b; EQ-25 |
| `w4c/readings/after-candidate/b-safe_lines.verdict.json` | `abd3fb6cca5b60eedc356af3aa7f0a70e7b21c30d8e98f74898874793105eb4e` | 2426 | `fnd/w4c` `drafts/w4c/readings/after-candidate/b-safe_lines.verdict.json` | the w4c commit; the registry's EQ-25, PWR-001 and W4C-F1 choices and W4C-F5 item; `EMCON.md` section 4b; EQ-25 |
| `w4c/readings/after-candidate/b-safe_lines_b.verdict.json` | `80e5c3c39a4e6ddc18d4bc55a8e8ba9901ccfecdec33bc4ef6375621763c57a4` | 2428 | `fnd/w4c` `drafts/w4c/readings/after-candidate/b-safe_lines_b.verdict.json` | the w4c commit; the registry's EQ-25, PWR-001 and W4C-F1 choices and W4C-F5 item; `EMCON.md` section 4b; EQ-25 |
| `w4c/readings/after-candidate/c-check_contracts.verdict.json` | `71e5c0272b99f439ad7daf464586375d991f7d0bd586de6a291a2043fdb32308` | 2941 | `fnd/w4c` `drafts/w4c/readings/after-candidate/c-check_contracts.verdict.json` | the w4c commit; the registry's EQ-25, PWR-001 and W4C-F1 choices and W4C-F5 item; `EMCON.md` section 4b; EQ-25 |
| `w4c/readings/after-candidate/c-check_contracts_a.verdict.json` | `1705c1e28beff3724c47bbbdacfea249576f69a65c6b4dbfe40b44271f90ac5a` | 2693 | `fnd/w4c` `drafts/w4c/readings/after-candidate/c-check_contracts_a.verdict.json` | the w4c commit; the registry's EQ-25, PWR-001 and W4C-F1 choices and W4C-F5 item; `EMCON.md` section 4b; EQ-25 |
| `w4c/readings/after-candidate/c-check_contracts_b.verdict.json` | `04bc910593d853fc3e132a404225b5b5b11ea25efb292174dc1cbe6bf8f56651` | 2438 | `fnd/w4c` `drafts/w4c/readings/after-candidate/c-check_contracts_b.verdict.json` | the w4c commit; the registry's EQ-25, PWR-001 and W4C-F1 choices and W4C-F5 item; `EMCON.md` section 4b; EQ-25 |
| `w4c/readings/after-candidate/c-check_contracts_c.verdict.json` | `c9649432834d93c64727196c4a994dab493543d8d858485e4d03f914f4d51a9e` | 2436 | `fnd/w4c` `drafts/w4c/readings/after-candidate/c-check_contracts_c.verdict.json` | the w4c commit; the registry's EQ-25, PWR-001 and W4C-F1 choices and W4C-F5 item; `EMCON.md` section 4b; EQ-25 |
| `w4c/readings/after-candidate/c-check_contracts_d.verdict.json` | `02bdc70a173596771915adf2ec8674b3e3056d6086936768367d1d414307ba5c` | 2438 | `fnd/w4c` `drafts/w4c/readings/after-candidate/c-check_contracts_d.verdict.json` | the w4c commit; the registry's EQ-25, PWR-001 and W4C-F1 choices and W4C-F5 item; `EMCON.md` section 4b; EQ-25 |
| `w4c/readings/after-candidate/c-check_contracts_e.verdict.json` | `495f84a5cc3563715af5fabe4a9146fba985fb542a8af2e92914742ff7f6023b` | 2165 | `fnd/w4c` `drafts/w4c/readings/after-candidate/c-check_contracts_e.verdict.json` | the w4c commit; the registry's EQ-25, PWR-001 and W4C-F1 choices and W4C-F5 item; `EMCON.md` section 4b; EQ-25 |
| `w4c/readings/after-candidate/c-check_contracts_p.verdict.json` | `91df696c1c4d17e8936e05cad4df25a251e74c9eeddda39065420eed77bc9540` | 1906 | `fnd/w4c` `drafts/w4c/readings/after-candidate/c-check_contracts_p.verdict.json` | the w4c commit; the registry's EQ-25, PWR-001 and W4C-F1 choices and W4C-F5 item; `EMCON.md` section 4b; EQ-25 |
| `w4c/readings/after-candidate/c-clock_check.verdict.json` | `edbb40f7ba510b6227abc96d7de53f2b6f05416e9290fd85a4dcc1f8f8cefe74` | 1221 | `fnd/w4c` `drafts/w4c/readings/after-candidate/c-clock_check.verdict.json` | the w4c commit; the registry's EQ-25, PWR-001 and W4C-F1 choices and W4C-F5 item; `EMCON.md` section 4b; EQ-25 |
| `w4c/readings/after-candidate/c-derate.verdict.json` | `b608ab3a2e1a49055bd34b335d38881a7b4af2047eb0239230d58c86cf64240a` | 4500 | `fnd/w4c` `drafts/w4c/readings/after-candidate/c-derate.verdict.json` | the w4c commit; the registry's EQ-25, PWR-001 and W4C-F1 choices and W4C-F5 item; `EMCON.md` section 4b; EQ-25 |
| `w4c/readings/after-candidate/c-edge_length.verdict.json` | `d3bf30c3720ed2d0f9013fc27405ea9ab7484f0f457dc18d4985aa947ef68e2e` | 7877 | `fnd/w4c` `drafts/w4c/readings/after-candidate/c-edge_length.verdict.json` | the w4c commit; the registry's EQ-25, PWR-001 and W4C-F1 choices and W4C-F5 item; `EMCON.md` section 4b; EQ-25 |
| `w4c/readings/after-candidate/c-erc_gate.verdict.json` | `677d373a080bb3294b44bfc06516647c3a10f509f37a333e6dd0373a40559893` | 1728 | `fnd/w4c` `drafts/w4c/readings/after-candidate/c-erc_gate.verdict.json` | the w4c commit; the registry's EQ-25, PWR-001 and W4C-F1 choices and W4C-F5 item; `EMCON.md` section 4b; EQ-25 |
| `w4c/readings/after-candidate/c-inhibit_chain_a.verdict.json` | `485e324090688ff3d14565f7721452ca25954db932108c401b8b4d4147e991dc` | 3754 | `fnd/w4c` `drafts/w4c/readings/after-candidate/c-inhibit_chain_a.verdict.json` | the w4c commit; the registry's EQ-25, PWR-001 and W4C-F1 choices and W4C-F5 item; `EMCON.md` section 4b; EQ-25 |
| `w4c/readings/after-candidate/c-inhibit_chain_b.verdict.json` | `384244b99e84a4f63c73e27616ae47aaab365087e7607299ee5cee1de6c01f85` | 4679 | `fnd/w4c` `drafts/w4c/readings/after-candidate/c-inhibit_chain_b.verdict.json` | the w4c commit; the registry's EQ-25, PWR-001 and W4C-F1 choices and W4C-F5 item; `EMCON.md` section 4b; EQ-25 |
| `w4c/readings/after-candidate/c-inhibit_chain_c.verdict.json` | `97599f9fdecbb08056b91118d892416e71a9f9ce9acefbb63b094ff457f3f927` | 3174 | `fnd/w4c` `drafts/w4c/readings/after-candidate/c-inhibit_chain_c.verdict.json` | the w4c commit; the registry's EQ-25, PWR-001 and W4C-F1 choices and W4C-F5 item; `EMCON.md` section 4b; EQ-25 |
| `w4c/readings/after-candidate/c-inhibit_chain_d.verdict.json` | `d63b1bfc5a90b3ca5a8d848bf81c8a225ff639b0e5078a073ff0dccf689dc7ff` | 3371 | `fnd/w4c` `drafts/w4c/readings/after-candidate/c-inhibit_chain_d.verdict.json` | the w4c commit; the registry's EQ-25, PWR-001 and W4C-F1 choices and W4C-F5 item; `EMCON.md` section 4b; EQ-25 |
| `w4c/readings/after-candidate/c-inhibit_chain_e.verdict.json` | `db962fcbcd05a9dcf505fe9f101d29cc4ff95ec641775f53450ff57093348271` | 2901 | `fnd/w4c` `drafts/w4c/readings/after-candidate/c-inhibit_chain_e.verdict.json` | the w4c commit; the registry's EQ-25, PWR-001 and W4C-F1 choices and W4C-F5 item; `EMCON.md` section 4b; EQ-25 |
| `w4c/readings/after-candidate/c-inhibit_chain_p.verdict.json` | `8fe2a85fa6001e308879ac1a9dc604ea4fb9b821baf080d8e046fd62ceffbcb2` | 2644 | `fnd/w4c` `drafts/w4c/readings/after-candidate/c-inhibit_chain_p.verdict.json` | the w4c commit; the registry's EQ-25, PWR-001 and W4C-F1 choices and W4C-F5 item; `EMCON.md` section 4b; EQ-25 |
| `w4c/readings/after-candidate/c-intent_rails.verdict.json` | `349ed82436f0057f7d13cedb7c6635c36c18a28fba68466738da199bdc5b527b` | 5603 | `fnd/w4c` `drafts/w4c/readings/after-candidate/c-intent_rails.verdict.json` | the w4c commit; the registry's EQ-25, PWR-001 and W4C-F1 choices and W4C-F5 item; `EMCON.md` section 4b; EQ-25 |
| `w4c/readings/after-candidate/c-interfaces.verdict.json` | `5b7db564081223883f2fe54e801ddfa79143a22b660d8fb8fd6babdcdc9d5044` | 1458 | `fnd/w4c` `drafts/w4c/readings/after-candidate/c-interfaces.verdict.json` | the w4c commit; the registry's EQ-25, PWR-001 and W4C-F1 choices and W4C-F5 item; `EMCON.md` section 4b; EQ-25 |
| `w4c/readings/after-candidate/c-interfaces_a.verdict.json` | `0be51bf7cfb023130beb4e919b01903ef6b3b1e69497425d9e6e6fd3c74ed32b` | 1627 | `fnd/w4c` `drafts/w4c/readings/after-candidate/c-interfaces_a.verdict.json` | the w4c commit; the registry's EQ-25, PWR-001 and W4C-F1 choices and W4C-F5 item; `EMCON.md` section 4b; EQ-25 |
| `w4c/readings/after-candidate/c-interfaces_b.verdict.json` | `fc5d4ffb398bbd0f6f87282358a8b3d1c02e64909f456b4c1949931903e447ad` | 1635 | `fnd/w4c` `drafts/w4c/readings/after-candidate/c-interfaces_b.verdict.json` | the w4c commit; the registry's EQ-25, PWR-001 and W4C-F1 choices and W4C-F5 item; `EMCON.md` section 4b; EQ-25 |
| `w4c/readings/after-candidate/c-interfaces_c.verdict.json` | `b833ba0b4c43966fcb8cd121a53bcd4b3bc036f987d2643f7f196316ed44340d` | 1633 | `fnd/w4c` `drafts/w4c/readings/after-candidate/c-interfaces_c.verdict.json` | the w4c commit; the registry's EQ-25, PWR-001 and W4C-F1 choices and W4C-F5 item; `EMCON.md` section 4b; EQ-25 |
| `w4c/readings/after-candidate/c-interfaces_d.verdict.json` | `b85e33416e0cb2084b2082e0167a63671a7b600fe3278e2d483d9b6e7da5170e` | 1621 | `fnd/w4c` `drafts/w4c/readings/after-candidate/c-interfaces_d.verdict.json` | the w4c commit; the registry's EQ-25, PWR-001 and W4C-F1 choices and W4C-F5 item; `EMCON.md` section 4b; EQ-25 |
| `w4c/readings/after-candidate/c-interfaces_e.verdict.json` | `9975a6f9daa9edfe8080e92101c93b95e2c9ab43f8658712bd2ce36bbd522fc7` | 1625 | `fnd/w4c` `drafts/w4c/readings/after-candidate/c-interfaces_e.verdict.json` | the w4c commit; the registry's EQ-25, PWR-001 and W4C-F1 choices and W4C-F5 item; `EMCON.md` section 4b; EQ-25 |
| `w4c/readings/after-candidate/c-interfaces_e5.verdict.json` | `24cc0393f7830feb44b708d3ea150709f8dc014339490383b0bda4977fa2e673` | 1802 | `fnd/w4c` `drafts/w4c/readings/after-candidate/c-interfaces_e5.verdict.json` | the w4c commit; the registry's EQ-25, PWR-001 and W4C-F1 choices and W4C-F5 item; `EMCON.md` section 4b; EQ-25 |
| `w4c/readings/after-candidate/c-interfaces_p.verdict.json` | `11294c1a095b579d7ceda9a7fc5b14469575d04758fd403fcab83114b79a6c67` | 1621 | `fnd/w4c` `drafts/w4c/readings/after-candidate/c-interfaces_p.verdict.json` | the w4c commit; the registry's EQ-25, PWR-001 and W4C-F1 choices and W4C-F5 item; `EMCON.md` section 4b; EQ-25 |
| `w4c/readings/after-candidate/c-pin_map_lands_c.verdict.json` | `f0a6d5293671f8dd4119c6b6b32fcae15860959e91e2a46e0d8d1cfa727a2c55` | 1252 | `fnd/w4c` `drafts/w4c/readings/after-candidate/c-pin_map_lands_c.verdict.json` | the w4c commit; the registry's EQ-25, PWR-001 and W4C-F1 choices and W4C-F5 item; `EMCON.md` section 4b; EQ-25 |
| `w4c/readings/after-candidate/c-port_protect.verdict.json` | `e83fcc602c19d29d15464cea1fc2839c03096451621ddc24d8765b775c69796d` | 1682 | `fnd/w4c` `drafts/w4c/readings/after-candidate/c-port_protect.verdict.json` | the w4c commit; the registry's EQ-25, PWR-001 and W4C-F1 choices and W4C-F5 item; `EMCON.md` section 4b; EQ-25 |
| `w4c/readings/after-candidate/c-port_protect_c.verdict.json` | `da44a136495c5356be12f69445d1ae0f510a87f58f68a2fbea7f2ce2a3e53009` | 1761 | `fnd/w4c` `drafts/w4c/readings/after-candidate/c-port_protect_c.verdict.json` | the w4c commit; the registry's EQ-25, PWR-001 and W4C-F1 choices and W4C-F5 item; `EMCON.md` section 4b; EQ-25 |
| `w4c/readings/after-candidate/c-power_path.log` | `72f2b0a4bcfe7f6cbccf4bd99f81c6ae2705d023ecae135ef0d7467f96a84802` | 6985 | `fnd/w4c` `drafts/w4c/readings/after-candidate/c-power_path.log` | the w4c commit; the registry's EQ-25, PWR-001 and W4C-F1 choices and W4C-F5 item; `EMCON.md` section 4b; EQ-25 |
| `w4c/readings/after-candidate/c-power_path.verdict.json` | `a1489b8eb0e2b343f6d6bc67a19c9f4b3ac1461a2fdb13481d3031e6b3f3e109` | 2508 | `fnd/w4c` `drafts/w4c/readings/after-candidate/c-power_path.verdict.json` | the w4c commit; the registry's EQ-25, PWR-001 and W4C-F1 choices and W4C-F5 item; `EMCON.md` section 4b; EQ-25 |
| `w4c/readings/after-candidate/c-power_sequence.log` | `ad56671acd272f38aacf57e81c31ca5a3651a44c660eed0671cb315aabfd3b35` | 832 | `fnd/w4c` `drafts/w4c/readings/after-candidate/c-power_sequence.log` | the w4c commit; the registry's EQ-25, PWR-001 and W4C-F1 choices and W4C-F5 item; `EMCON.md` section 4b; EQ-25 |
| `w4c/readings/after-candidate/c-power_sequence.verdict.json` | `64304c882cef28161304e94be94c9a56163d4a10198add177a4c66f6fcac9536` | 1733 | `fnd/w4c` `drafts/w4c/readings/after-candidate/c-power_sequence.verdict.json` | the w4c commit; the registry's EQ-25, PWR-001 and W4C-F1 choices and W4C-F5 item; `EMCON.md` section 4b; EQ-25 |
| `w4c/readings/after-candidate/c-safe_lines.log` | `17f084df655a6dc955ba963086c6121a87a3318fe9635dbe378dfcbfdb3fd7da` | 1419 | `fnd/w4c` `drafts/w4c/readings/after-candidate/c-safe_lines.log` | the w4c commit; the registry's EQ-25, PWR-001 and W4C-F1 choices and W4C-F5 item; `EMCON.md` section 4b; EQ-25 |
| `w4c/readings/after-candidate/d-check_contracts.verdict.json` | `2b4fa3e3974c7722573070a9043ef97676f1e0e78cb950457256ba2cf2e02cca` | 2941 | `fnd/w4c` `drafts/w4c/readings/after-candidate/d-check_contracts.verdict.json` | the w4c commit; the registry's EQ-25, PWR-001 and W4C-F1 choices and W4C-F5 item; `EMCON.md` section 4b; EQ-25 |
| `w4c/readings/after-candidate/d-check_contracts_a.verdict.json` | `7dba55c0e51c74da02217e17419b1a3c663438376fc761b9ac5b85c091900027` | 2693 | `fnd/w4c` `drafts/w4c/readings/after-candidate/d-check_contracts_a.verdict.json` | the w4c commit; the registry's EQ-25, PWR-001 and W4C-F1 choices and W4C-F5 item; `EMCON.md` section 4b; EQ-25 |
| `w4c/readings/after-candidate/d-check_contracts_b.verdict.json` | `87c844cd90a08ede555e579e8c8ba15fc151b1788b1005b2c27949b7497ea576` | 2438 | `fnd/w4c` `drafts/w4c/readings/after-candidate/d-check_contracts_b.verdict.json` | the w4c commit; the registry's EQ-25, PWR-001 and W4C-F1 choices and W4C-F5 item; `EMCON.md` section 4b; EQ-25 |
| `w4c/readings/after-candidate/d-check_contracts_c.verdict.json` | `3554843aa880044e66dfa902c79f29c2b32b6cd81a46a0366e48b65555cd8872` | 2436 | `fnd/w4c` `drafts/w4c/readings/after-candidate/d-check_contracts_c.verdict.json` | the w4c commit; the registry's EQ-25, PWR-001 and W4C-F1 choices and W4C-F5 item; `EMCON.md` section 4b; EQ-25 |
| `w4c/readings/after-candidate/d-check_contracts_d.verdict.json` | `90e433f494f066c0c1011d1a8528f8a4edf4d848c12ad3d3167684403346f9c9` | 2438 | `fnd/w4c` `drafts/w4c/readings/after-candidate/d-check_contracts_d.verdict.json` | the w4c commit; the registry's EQ-25, PWR-001 and W4C-F1 choices and W4C-F5 item; `EMCON.md` section 4b; EQ-25 |
| `w4c/readings/after-candidate/d-check_contracts_e.verdict.json` | `11845b1404553c98c65b4da0ed3886a23a0ca72796fa333cafefc302ccc7b517` | 2165 | `fnd/w4c` `drafts/w4c/readings/after-candidate/d-check_contracts_e.verdict.json` | the w4c commit; the registry's EQ-25, PWR-001 and W4C-F1 choices and W4C-F5 item; `EMCON.md` section 4b; EQ-25 |
| `w4c/readings/after-candidate/d-check_contracts_p.verdict.json` | `af946fe5ce084850b43e643cd3f57cb3c4b29ee5fb899637351fe07ae75881cb` | 1906 | `fnd/w4c` `drafts/w4c/readings/after-candidate/d-check_contracts_p.verdict.json` | the w4c commit; the registry's EQ-25, PWR-001 and W4C-F1 choices and W4C-F5 item; `EMCON.md` section 4b; EQ-25 |
| `w4c/readings/after-candidate/d-clock_check.verdict.json` | `a70756609e918f16dbfe9dc488ee940bc94efc84ddc86b30e53d9294777cef1f` | 1218 | `fnd/w4c` `drafts/w4c/readings/after-candidate/d-clock_check.verdict.json` | the w4c commit; the registry's EQ-25, PWR-001 and W4C-F1 choices and W4C-F5 item; `EMCON.md` section 4b; EQ-25 |
| `w4c/readings/after-candidate/d-derate.verdict.json` | `9ace0ab3cfffd69ee08e386b3c496b79314fa0d17717a2f76ecf86b466056f01` | 1250 | `fnd/w4c` `drafts/w4c/readings/after-candidate/d-derate.verdict.json` | the w4c commit; the registry's EQ-25, PWR-001 and W4C-F1 choices and W4C-F5 item; `EMCON.md` section 4b; EQ-25 |
| `w4c/readings/after-candidate/d-edge_length.verdict.json` | `e645c5bb352430f36207d30465596e6f14ac3e4de6108225c3dea83613709565` | 6760 | `fnd/w4c` `drafts/w4c/readings/after-candidate/d-edge_length.verdict.json` | the w4c commit; the registry's EQ-25, PWR-001 and W4C-F1 choices and W4C-F5 item; `EMCON.md` section 4b; EQ-25 |
| `w4c/readings/after-candidate/d-erc_gate.verdict.json` | `4a16d3eade99d56454479bddfa1be54e0eda315c03dd8c4dabfe1d7926f835cd` | 1719 | `fnd/w4c` `drafts/w4c/readings/after-candidate/d-erc_gate.verdict.json` | the w4c commit; the registry's EQ-25, PWR-001 and W4C-F1 choices and W4C-F5 item; `EMCON.md` section 4b; EQ-25 |
| `w4c/readings/after-candidate/d-inhibit_chain_a.verdict.json` | `5af36e2760a13296102c2dafef867cabee341e1c3175e0c517603b9a944065a6` | 3754 | `fnd/w4c` `drafts/w4c/readings/after-candidate/d-inhibit_chain_a.verdict.json` | the w4c commit; the registry's EQ-25, PWR-001 and W4C-F1 choices and W4C-F5 item; `EMCON.md` section 4b; EQ-25 |
| `w4c/readings/after-candidate/d-inhibit_chain_b.verdict.json` | `9eec86b3fab27b1a1e3606db694e55916bf416b565930d8a1cccc3d4f1b41859` | 4679 | `fnd/w4c` `drafts/w4c/readings/after-candidate/d-inhibit_chain_b.verdict.json` | the w4c commit; the registry's EQ-25, PWR-001 and W4C-F1 choices and W4C-F5 item; `EMCON.md` section 4b; EQ-25 |
| `w4c/readings/after-candidate/d-inhibit_chain_c.verdict.json` | `ae966e9cf61924f79a79ac3f9c00ac0a31058c5cde377af68437266af207e71d` | 3174 | `fnd/w4c` `drafts/w4c/readings/after-candidate/d-inhibit_chain_c.verdict.json` | the w4c commit; the registry's EQ-25, PWR-001 and W4C-F1 choices and W4C-F5 item; `EMCON.md` section 4b; EQ-25 |
| `w4c/readings/after-candidate/d-inhibit_chain_d.verdict.json` | `ba73bc6d914a092376de7b4fa8b2e7c70217c5a623914be19a35651764d1ee48` | 3371 | `fnd/w4c` `drafts/w4c/readings/after-candidate/d-inhibit_chain_d.verdict.json` | the w4c commit; the registry's EQ-25, PWR-001 and W4C-F1 choices and W4C-F5 item; `EMCON.md` section 4b; EQ-25 |
| `w4c/readings/after-candidate/d-inhibit_chain_e.verdict.json` | `80f62dbb6e2369b0f313db8470bb0ea6faf216e26a7ebe0317f39a48f047ab6c` | 2901 | `fnd/w4c` `drafts/w4c/readings/after-candidate/d-inhibit_chain_e.verdict.json` | the w4c commit; the registry's EQ-25, PWR-001 and W4C-F1 choices and W4C-F5 item; `EMCON.md` section 4b; EQ-25 |
| `w4c/readings/after-candidate/d-inhibit_chain_p.verdict.json` | `9e4b84ba99a60cfadff1376ebb729f5c255a01e53e65755409e6b35d0da40970` | 2644 | `fnd/w4c` `drafts/w4c/readings/after-candidate/d-inhibit_chain_p.verdict.json` | the w4c commit; the registry's EQ-25, PWR-001 and W4C-F1 choices and W4C-F5 item; `EMCON.md` section 4b; EQ-25 |
| `w4c/readings/after-candidate/d-intent_rails.verdict.json` | `67aaeeed0721d31001f263f554b86b5facd5a7dc6a784d53d9f2cd55496d9576` | 8336 | `fnd/w4c` `drafts/w4c/readings/after-candidate/d-intent_rails.verdict.json` | the w4c commit; the registry's EQ-25, PWR-001 and W4C-F1 choices and W4C-F5 item; `EMCON.md` section 4b; EQ-25 |
| `w4c/readings/after-candidate/d-interfaces.verdict.json` | `6c151d54cf56212b5f70a4e3ddc13d9ac8853558108ceb7300a0265974bcd7ad` | 1458 | `fnd/w4c` `drafts/w4c/readings/after-candidate/d-interfaces.verdict.json` | the w4c commit; the registry's EQ-25, PWR-001 and W4C-F1 choices and W4C-F5 item; `EMCON.md` section 4b; EQ-25 |
| `w4c/readings/after-candidate/d-interfaces_a.verdict.json` | `9a4e4d83a67ba9e6449061f277fbd938e485b06ab6d2c9a958b1b7cda7375e4b` | 1627 | `fnd/w4c` `drafts/w4c/readings/after-candidate/d-interfaces_a.verdict.json` | the w4c commit; the registry's EQ-25, PWR-001 and W4C-F1 choices and W4C-F5 item; `EMCON.md` section 4b; EQ-25 |
| `w4c/readings/after-candidate/d-interfaces_b.verdict.json` | `991eaaa140c7eade61a6a1eb20fe91fbdb960b21fe4653468489bef775046e8f` | 1635 | `fnd/w4c` `drafts/w4c/readings/after-candidate/d-interfaces_b.verdict.json` | the w4c commit; the registry's EQ-25, PWR-001 and W4C-F1 choices and W4C-F5 item; `EMCON.md` section 4b; EQ-25 |
| `w4c/readings/after-candidate/d-interfaces_c.verdict.json` | `842fb4bb1f8fc6828ab9e93d02a4e8059e76b036a3278008068141768d6316ee` | 1633 | `fnd/w4c` `drafts/w4c/readings/after-candidate/d-interfaces_c.verdict.json` | the w4c commit; the registry's EQ-25, PWR-001 and W4C-F1 choices and W4C-F5 item; `EMCON.md` section 4b; EQ-25 |
| `w4c/readings/after-candidate/d-interfaces_d.verdict.json` | `fd0ed90e48adb2d4bc469ba929c20fdf353d9bdd0318bc39b6176e7ca16ff1da` | 1621 | `fnd/w4c` `drafts/w4c/readings/after-candidate/d-interfaces_d.verdict.json` | the w4c commit; the registry's EQ-25, PWR-001 and W4C-F1 choices and W4C-F5 item; `EMCON.md` section 4b; EQ-25 |
| `w4c/readings/after-candidate/d-interfaces_e.verdict.json` | `0d44ef1c3ffad49107039e7397b65378bce19e8cdf84a731613d124edb804b1e` | 1625 | `fnd/w4c` `drafts/w4c/readings/after-candidate/d-interfaces_e.verdict.json` | the w4c commit; the registry's EQ-25, PWR-001 and W4C-F1 choices and W4C-F5 item; `EMCON.md` section 4b; EQ-25 |
| `w4c/readings/after-candidate/d-interfaces_e5.verdict.json` | `c046db054c65ea212f21449dc532c4bd14155170162979857367db746bdee95b` | 1802 | `fnd/w4c` `drafts/w4c/readings/after-candidate/d-interfaces_e5.verdict.json` | the w4c commit; the registry's EQ-25, PWR-001 and W4C-F1 choices and W4C-F5 item; `EMCON.md` section 4b; EQ-25 |
| `w4c/readings/after-candidate/d-interfaces_p.verdict.json` | `a05423cbac14fc9574dad958ab7734c75f125e1a63cab3d53b27c81983a0f3ec` | 1621 | `fnd/w4c` `drafts/w4c/readings/after-candidate/d-interfaces_p.verdict.json` | the w4c commit; the registry's EQ-25, PWR-001 and W4C-F1 choices and W4C-F5 item; `EMCON.md` section 4b; EQ-25 |
| `w4c/readings/after-candidate/d-pin_map_lands_d.verdict.json` | `6cb12e993bb4c18a9f9b838d33b42095462e8cb917203cb8058ced6ead23c9e6` | 1249 | `fnd/w4c` `drafts/w4c/readings/after-candidate/d-pin_map_lands_d.verdict.json` | the w4c commit; the registry's EQ-25, PWR-001 and W4C-F1 choices and W4C-F5 item; `EMCON.md` section 4b; EQ-25 |
| `w4c/readings/after-candidate/d-port_protect.verdict.json` | `de84f361e6a47a706969d5bdb4ea0b0acbfdbf52adade7132e432623ce793878` | 1677 | `fnd/w4c` `drafts/w4c/readings/after-candidate/d-port_protect.verdict.json` | the w4c commit; the registry's EQ-25, PWR-001 and W4C-F1 choices and W4C-F5 item; `EMCON.md` section 4b; EQ-25 |
| `w4c/readings/after-candidate/d-port_protect_d.verdict.json` | `845a56bbaa8fceefe66b8cca8421c531d1ed76d9dd011521b1fa023e91b5ebd1` | 1756 | `fnd/w4c` `drafts/w4c/readings/after-candidate/d-port_protect_d.verdict.json` | the w4c commit; the registry's EQ-25, PWR-001 and W4C-F1 choices and W4C-F5 item; `EMCON.md` section 4b; EQ-25 |
| `w4c/readings/after-candidate/d-safe_lines.verdict.json` | `5f223d7c6c3deb15abc9b71f124961c2e237875c22e25eb2aeaa1778f3d447c0` | 1857 | `fnd/w4c` `drafts/w4c/readings/after-candidate/d-safe_lines.verdict.json` | the w4c commit; the registry's EQ-25, PWR-001 and W4C-F1 choices and W4C-F5 item; `EMCON.md` section 4b; EQ-25 |
| `w4c/readings/after-candidate/d-safe_lines_d.verdict.json` | `4cc679ec018156694b831e1cf8ad462750057c14f4060fd99c1827912a140080` | 1859 | `fnd/w4c` `drafts/w4c/readings/after-candidate/d-safe_lines_d.verdict.json` | the w4c commit; the registry's EQ-25, PWR-001 and W4C-F1 choices and W4C-F5 item; `EMCON.md` section 4b; EQ-25 |
| `w4c/readings/after-candidate/fail-safe-states-TX_INHIBIT_n.txt` | `43c0ae7dfb94f18441c15111faeb88a7bf96c0c5a04f88c8739d8ca9de82c89a` | 1855 | `fnd/w4c` `drafts/w4c/readings/after-candidate/fail-safe-states-TX_INHIBIT_n.txt` | the w4c commit; the registry's EQ-25, PWR-001 and W4C-F1 choices and W4C-F5 item; `EMCON.md` section 4b; EQ-25 |
| `w4c/readings/after-candidate/walk-tx_inhibit-report.txt` | `9876ee6807b1984f2fd495984749017a8d5ae3758595d877b8e9637d524df118` | 16204 | `fnd/w4c` `drafts/w4c/readings/after-candidate/walk-tx_inhibit-report.txt` | the w4c commit; the registry's EQ-25, PWR-001 and W4C-F1 choices and W4C-F5 item; `EMCON.md` section 4b; EQ-25 |
| `w4c/readings/before-main-91894cd7/a-check_contracts.verdict.json` | `8c8545290cec8296e854945dea1ea000941bb0b81aed9a3020555d3595d28ca1` | 2941 | `fnd/w4c` `drafts/w4c/readings/before-main-91894cd7/a-check_contracts.verdict.json` | the w4c commit; the registry's EQ-25, PWR-001 and W4C-F1 choices and W4C-F5 item; `EMCON.md` section 4b; EQ-25 |
| `w4c/readings/before-main-91894cd7/a-check_contracts_a.verdict.json` | `ca722bef33372371e17044e6c7a60087d670947762dd501d7134ab7a5b6f0d03` | 2693 | `fnd/w4c` `drafts/w4c/readings/before-main-91894cd7/a-check_contracts_a.verdict.json` | the w4c commit; the registry's EQ-25, PWR-001 and W4C-F1 choices and W4C-F5 item; `EMCON.md` section 4b; EQ-25 |
| `w4c/readings/before-main-91894cd7/a-check_contracts_b.verdict.json` | `aa1c8fddd73e130446f6fe109a7cbff26fe963551cb28552dd53546e26a6a564` | 2438 | `fnd/w4c` `drafts/w4c/readings/before-main-91894cd7/a-check_contracts_b.verdict.json` | the w4c commit; the registry's EQ-25, PWR-001 and W4C-F1 choices and W4C-F5 item; `EMCON.md` section 4b; EQ-25 |
| `w4c/readings/before-main-91894cd7/a-check_contracts_c.verdict.json` | `131f8190d781c1a96969c05218108272b46ac03a83e72027383799083ab76472` | 2436 | `fnd/w4c` `drafts/w4c/readings/before-main-91894cd7/a-check_contracts_c.verdict.json` | the w4c commit; the registry's EQ-25, PWR-001 and W4C-F1 choices and W4C-F5 item; `EMCON.md` section 4b; EQ-25 |
| `w4c/readings/before-main-91894cd7/a-check_contracts_d.verdict.json` | `6137d5386976fd3c55c44e22bc0c33b31651d26179b5808e263d1f4b642b3f2c` | 2438 | `fnd/w4c` `drafts/w4c/readings/before-main-91894cd7/a-check_contracts_d.verdict.json` | the w4c commit; the registry's EQ-25, PWR-001 and W4C-F1 choices and W4C-F5 item; `EMCON.md` section 4b; EQ-25 |
| `w4c/readings/before-main-91894cd7/a-check_contracts_e.verdict.json` | `1d9b432cdc2d385812f2799628fc298b3589fb036ae84654bb767a020e64cb0f` | 2165 | `fnd/w4c` `drafts/w4c/readings/before-main-91894cd7/a-check_contracts_e.verdict.json` | the w4c commit; the registry's EQ-25, PWR-001 and W4C-F1 choices and W4C-F5 item; `EMCON.md` section 4b; EQ-25 |
| `w4c/readings/before-main-91894cd7/a-check_contracts_p.verdict.json` | `e0e02b76bf5ef3d6d85f6e2e5b6b616ae9f0d5ee7e55e78f136c5cc9e49faa1e` | 1906 | `fnd/w4c` `drafts/w4c/readings/before-main-91894cd7/a-check_contracts_p.verdict.json` | the w4c commit; the registry's EQ-25, PWR-001 and W4C-F1 choices and W4C-F5 item; `EMCON.md` section 4b; EQ-25 |
| `w4c/readings/before-main-91894cd7/a-clock_check.verdict.json` | `4ac305dd31c80a03dda24e4b990fe5d0a0695d002de6bda1b6380f0116c52a86` | 1076 | `fnd/w4c` `drafts/w4c/readings/before-main-91894cd7/a-clock_check.verdict.json` | the w4c commit; the registry's EQ-25, PWR-001 and W4C-F1 choices and W4C-F5 item; `EMCON.md` section 4b; EQ-25 |
| `w4c/readings/before-main-91894cd7/a-derate.verdict.json` | `02382aeb517ab64be0fa5800513f9a6e1f7c38ccd08e9ccb90dbd3d1b1440f74` | 1254 | `fnd/w4c` `drafts/w4c/readings/before-main-91894cd7/a-derate.verdict.json` | the w4c commit; the registry's EQ-25, PWR-001 and W4C-F1 choices and W4C-F5 item; `EMCON.md` section 4b; EQ-25 |
| `w4c/readings/before-main-91894cd7/a-edge_length.verdict.json` | `8cb536192a4616bb947c5ed8a8837b81a24f4a2f5000b52462ab6245513a4849` | 9116 | `fnd/w4c` `drafts/w4c/readings/before-main-91894cd7/a-edge_length.verdict.json` | the w4c commit; the registry's EQ-25, PWR-001 and W4C-F1 choices and W4C-F5 item; `EMCON.md` section 4b; EQ-25 |
| `w4c/readings/before-main-91894cd7/a-energy_chain.verdict.json` | `de49fb23d41234354d56c62c94c26a7f1f16ac34042fb40ef3c22d94ebaecd5b` | 2479 | `fnd/w4c` `drafts/w4c/readings/before-main-91894cd7/a-energy_chain.verdict.json` | the w4c commit; the registry's EQ-25, PWR-001 and W4C-F1 choices and W4C-F5 item; `EMCON.md` section 4b; EQ-25 |
| `w4c/readings/before-main-91894cd7/a-energy_chain_a.verdict.json` | `8282f29355ee61a5837cb72f893192af65923f3979cb1489111b5eca1c3db4b2` | 1750 | `fnd/w4c` `drafts/w4c/readings/before-main-91894cd7/a-energy_chain_a.verdict.json` | the w4c commit; the registry's EQ-25, PWR-001 and W4C-F1 choices and W4C-F5 item; `EMCON.md` section 4b; EQ-25 |
| `w4c/readings/before-main-91894cd7/a-energy_chain_b.verdict.json` | `18d536090677120fc858593a14546214ac94dd402bcb34bb98748cafcf433200` | 1612 | `fnd/w4c` `drafts/w4c/readings/before-main-91894cd7/a-energy_chain_b.verdict.json` | the w4c commit; the registry's EQ-25, PWR-001 and W4C-F1 choices and W4C-F5 item; `EMCON.md` section 4b; EQ-25 |
| `w4c/readings/before-main-91894cd7/a-energy_chain_e.verdict.json` | `7f8bafb07f3060f004765f624361d65d3b5ad9791357064fe77695d17aa029bb` | 1750 | `fnd/w4c` `drafts/w4c/readings/before-main-91894cd7/a-energy_chain_e.verdict.json` | the w4c commit; the registry's EQ-25, PWR-001 and W4C-F1 choices and W4C-F5 item; `EMCON.md` section 4b; EQ-25 |
| `w4c/readings/before-main-91894cd7/a-energy_chain_e5.verdict.json` | `84814620873f5806733b2c848b195eedaca2cfc724f3a94ce9989d87ce547d77` | 1558 | `fnd/w4c` `drafts/w4c/readings/before-main-91894cd7/a-energy_chain_e5.verdict.json` | the w4c commit; the registry's EQ-25, PWR-001 and W4C-F1 choices and W4C-F5 item; `EMCON.md` section 4b; EQ-25 |
| `w4c/readings/before-main-91894cd7/a-energy_chain_p.verdict.json` | `4934accc39ecaddb43f61d53be43ab16b0f6b00383720190ad67baf271e4f10d` | 1606 | `fnd/w4c` `drafts/w4c/readings/before-main-91894cd7/a-energy_chain_p.verdict.json` | the w4c commit; the registry's EQ-25, PWR-001 and W4C-F1 choices and W4C-F5 item; `EMCON.md` section 4b; EQ-25 |
| `w4c/readings/before-main-91894cd7/a-erc_gate.verdict.json` | `4d57c976dd4710a2930fb4bbf4b95e3847eaa1a98dadc75de2b307975c1e82d7` | 1724 | `fnd/w4c` `drafts/w4c/readings/before-main-91894cd7/a-erc_gate.verdict.json` | the w4c commit; the registry's EQ-25, PWR-001 and W4C-F1 choices and W4C-F5 item; `EMCON.md` section 4b; EQ-25 |
| `w4c/readings/before-main-91894cd7/a-inhibit_chain_a.verdict.json` | `10b6b8ad84e28f3d8fc2213da72da04f74e6a89ba985bbe0f402ad80c5b4d0db` | 3995 | `fnd/w4c` `drafts/w4c/readings/before-main-91894cd7/a-inhibit_chain_a.verdict.json` | the w4c commit; the registry's EQ-25, PWR-001 and W4C-F1 choices and W4C-F5 item; `EMCON.md` section 4b; EQ-25 |
| `w4c/readings/before-main-91894cd7/a-inhibit_chain_b.verdict.json` | `c66bbc8496d94574a119e0bb965ba58fd636abd68da028eea4e2cdc92fe232ea` | 4928 | `fnd/w4c` `drafts/w4c/readings/before-main-91894cd7/a-inhibit_chain_b.verdict.json` | the w4c commit; the registry's EQ-25, PWR-001 and W4C-F1 choices and W4C-F5 item; `EMCON.md` section 4b; EQ-25 |
| `w4c/readings/before-main-91894cd7/a-inhibit_chain_c.verdict.json` | `8659418f2b8b4d763f53ac082f83e197ce2b4fc8d6f1182c8140be7006934e16` | 3424 | `fnd/w4c` `drafts/w4c/readings/before-main-91894cd7/a-inhibit_chain_c.verdict.json` | the w4c commit; the registry's EQ-25, PWR-001 and W4C-F1 choices and W4C-F5 item; `EMCON.md` section 4b; EQ-25 |
| `w4c/readings/before-main-91894cd7/a-inhibit_chain_d.verdict.json` | `1de79fddf421d4130a7bed0f40baffae12758edacd1e5d898aed7cd034c1a9b3` | 3498 | `fnd/w4c` `drafts/w4c/readings/before-main-91894cd7/a-inhibit_chain_d.verdict.json` | the w4c commit; the registry's EQ-25, PWR-001 and W4C-F1 choices and W4C-F5 item; `EMCON.md` section 4b; EQ-25 |
| `w4c/readings/before-main-91894cd7/a-inhibit_chain_e.verdict.json` | `8855ba294eca69ec0ac009cef72c987d13b4bc1e81d8d25b28fd8819c269ac39` | 2901 | `fnd/w4c` `drafts/w4c/readings/before-main-91894cd7/a-inhibit_chain_e.verdict.json` | the w4c commit; the registry's EQ-25, PWR-001 and W4C-F1 choices and W4C-F5 item; `EMCON.md` section 4b; EQ-25 |
| `w4c/readings/before-main-91894cd7/a-inhibit_chain_p.verdict.json` | `2bc21341a1d63db1f1db722003d597eaf27fe38f53390508392d8e180d9024fb` | 2644 | `fnd/w4c` `drafts/w4c/readings/before-main-91894cd7/a-inhibit_chain_p.verdict.json` | the w4c commit; the registry's EQ-25, PWR-001 and W4C-F1 choices and W4C-F5 item; `EMCON.md` section 4b; EQ-25 |
| `w4c/readings/before-main-91894cd7/a-intent_rails.verdict.json` | `bb31296a2537d37b3e93b9790484da3e74269b7bf3153ea051f7f4eaa947e5a3` | 11046 | `fnd/w4c` `drafts/w4c/readings/before-main-91894cd7/a-intent_rails.verdict.json` | the w4c commit; the registry's EQ-25, PWR-001 and W4C-F1 choices and W4C-F5 item; `EMCON.md` section 4b; EQ-25 |
| `w4c/readings/before-main-91894cd7/a-interfaces.verdict.json` | `bb7aaa3b568158250c4af67716293c87bb27bd9fbe007b4038efee1eefa56e82` | 1458 | `fnd/w4c` `drafts/w4c/readings/before-main-91894cd7/a-interfaces.verdict.json` | the w4c commit; the registry's EQ-25, PWR-001 and W4C-F1 choices and W4C-F5 item; `EMCON.md` section 4b; EQ-25 |
| `w4c/readings/before-main-91894cd7/a-interfaces_a.verdict.json` | `fdf981dbe5b902850925e76ef5dc5ade54cbefd03664b7dc4d7a7d9e5162d32d` | 1627 | `fnd/w4c` `drafts/w4c/readings/before-main-91894cd7/a-interfaces_a.verdict.json` | the w4c commit; the registry's EQ-25, PWR-001 and W4C-F1 choices and W4C-F5 item; `EMCON.md` section 4b; EQ-25 |
| `w4c/readings/before-main-91894cd7/a-interfaces_b.verdict.json` | `5b6d85e46eaa011bd545a20ca634cace4fbbea1a8b8a683098e5672febb585d6` | 1635 | `fnd/w4c` `drafts/w4c/readings/before-main-91894cd7/a-interfaces_b.verdict.json` | the w4c commit; the registry's EQ-25, PWR-001 and W4C-F1 choices and W4C-F5 item; `EMCON.md` section 4b; EQ-25 |
| `w4c/readings/before-main-91894cd7/a-interfaces_c.verdict.json` | `18b43a950d4cde33cfdf8fd16788528b6acc4836d67fc08f1e18b938d7821b7a` | 1633 | `fnd/w4c` `drafts/w4c/readings/before-main-91894cd7/a-interfaces_c.verdict.json` | the w4c commit; the registry's EQ-25, PWR-001 and W4C-F1 choices and W4C-F5 item; `EMCON.md` section 4b; EQ-25 |
| `w4c/readings/before-main-91894cd7/a-interfaces_d.verdict.json` | `88e23a6b777b4a80d1b06d2075db0a498b530061b89bfb74e32538696b5de836` | 1621 | `fnd/w4c` `drafts/w4c/readings/before-main-91894cd7/a-interfaces_d.verdict.json` | the w4c commit; the registry's EQ-25, PWR-001 and W4C-F1 choices and W4C-F5 item; `EMCON.md` section 4b; EQ-25 |
| `w4c/readings/before-main-91894cd7/a-interfaces_e.verdict.json` | `87d526d1f085f228190cee6836c268eb9a705c291d22638b4de4db0d8cbe08cd` | 1625 | `fnd/w4c` `drafts/w4c/readings/before-main-91894cd7/a-interfaces_e.verdict.json` | the w4c commit; the registry's EQ-25, PWR-001 and W4C-F1 choices and W4C-F5 item; `EMCON.md` section 4b; EQ-25 |
| `w4c/readings/before-main-91894cd7/a-interfaces_e5.verdict.json` | `ecd5761b8ebe36b729afd10f713b4a0f799075c65230752ca8819b1e1a04be79` | 1802 | `fnd/w4c` `drafts/w4c/readings/before-main-91894cd7/a-interfaces_e5.verdict.json` | the w4c commit; the registry's EQ-25, PWR-001 and W4C-F1 choices and W4C-F5 item; `EMCON.md` section 4b; EQ-25 |
| `w4c/readings/before-main-91894cd7/a-interfaces_p.verdict.json` | `3c6fae631de3e1e743cf94734f105e090a8bb81941b1caf54a2ff0b90b1d956e` | 1621 | `fnd/w4c` `drafts/w4c/readings/before-main-91894cd7/a-interfaces_p.verdict.json` | the w4c commit; the registry's EQ-25, PWR-001 and W4C-F1 choices and W4C-F5 item; `EMCON.md` section 4b; EQ-25 |
| `w4c/readings/before-main-91894cd7/a-pin_map_lands_a.verdict.json` | `6aa5a8638f960498717a2c22a52af3bea900be43f0d587b084c4d8551087025f` | 1250 | `fnd/w4c` `drafts/w4c/readings/before-main-91894cd7/a-pin_map_lands_a.verdict.json` | the w4c commit; the registry's EQ-25, PWR-001 and W4C-F1 choices and W4C-F5 item; `EMCON.md` section 4b; EQ-25 |
| `w4c/readings/before-main-91894cd7/a-port_protect.verdict.json` | `990d870daafe12d3f3bef3938acfab90b99a53caddea8eb2cbcfd8261c0ae93c` | 1679 | `fnd/w4c` `drafts/w4c/readings/before-main-91894cd7/a-port_protect.verdict.json` | the w4c commit; the registry's EQ-25, PWR-001 and W4C-F1 choices and W4C-F5 item; `EMCON.md` section 4b; EQ-25 |
| `w4c/readings/before-main-91894cd7/a-port_protect_a.verdict.json` | `d7ca63612745992298dcffaf8a819559a3b9926144c242be44afba9887806252` | 1758 | `fnd/w4c` `drafts/w4c/readings/before-main-91894cd7/a-port_protect_a.verdict.json` | the w4c commit; the registry's EQ-25, PWR-001 and W4C-F1 choices and W4C-F5 item; `EMCON.md` section 4b; EQ-25 |
| `w4c/readings/before-main-91894cd7/a-power_sequence.verdict.json` | `9e60437f7cfe858d912f66929c2a1c2d7e8b868daecd576e5e86267806f8c45d` | 1698 | `fnd/w4c` `drafts/w4c/readings/before-main-91894cd7/a-power_sequence.verdict.json` | the w4c commit; the registry's EQ-25, PWR-001 and W4C-F1 choices and W4C-F5 item; `EMCON.md` section 4b; EQ-25 |
| `w4c/readings/before-main-91894cd7/a-safe_lines.verdict.json` | `c574dd9338d37d95277ccead4383ac7ba3a8112b56a9e91575b4208afe578cc7` | 2581 | `fnd/w4c` `drafts/w4c/readings/before-main-91894cd7/a-safe_lines.verdict.json` | the w4c commit; the registry's EQ-25, PWR-001 and W4C-F1 choices and W4C-F5 item; `EMCON.md` section 4b; EQ-25 |
| `w4c/readings/before-main-91894cd7/a-safe_lines_a.verdict.json` | `5d7206976d2cf193780678923c905a70bc5051d12476b24fb7d66a3a2f3bbc19` | 2583 | `fnd/w4c` `drafts/w4c/readings/before-main-91894cd7/a-safe_lines_a.verdict.json` | the w4c commit; the registry's EQ-25, PWR-001 and W4C-F1 choices and W4C-F5 item; `EMCON.md` section 4b; EQ-25 |
| `w4c/readings/before-main-91894cd7/b-check_contracts.verdict.json` | `be50c2056597c9ecddfffd66b33e9c501344eb4ed14450d201d8555ade821dbc` | 2941 | `fnd/w4c` `drafts/w4c/readings/before-main-91894cd7/b-check_contracts.verdict.json` | the w4c commit; the registry's EQ-25, PWR-001 and W4C-F1 choices and W4C-F5 item; `EMCON.md` section 4b; EQ-25 |
| `w4c/readings/before-main-91894cd7/b-check_contracts_a.verdict.json` | `0c9be12d4ba8e648707f2480c388c624cef47ac4f567e9c9487d787feec17bb4` | 2693 | `fnd/w4c` `drafts/w4c/readings/before-main-91894cd7/b-check_contracts_a.verdict.json` | the w4c commit; the registry's EQ-25, PWR-001 and W4C-F1 choices and W4C-F5 item; `EMCON.md` section 4b; EQ-25 |
| `w4c/readings/before-main-91894cd7/b-check_contracts_b.verdict.json` | `1bfe27e2944d0a84fd4e1d50585e569e3238edf665da01ed54f383c2be5cf000` | 2438 | `fnd/w4c` `drafts/w4c/readings/before-main-91894cd7/b-check_contracts_b.verdict.json` | the w4c commit; the registry's EQ-25, PWR-001 and W4C-F1 choices and W4C-F5 item; `EMCON.md` section 4b; EQ-25 |
| `w4c/readings/before-main-91894cd7/b-check_contracts_c.verdict.json` | `0afc3c66fb3048b6979383aa822d30c203693f0a5c3e4f7a2fac74ea3e180003` | 2436 | `fnd/w4c` `drafts/w4c/readings/before-main-91894cd7/b-check_contracts_c.verdict.json` | the w4c commit; the registry's EQ-25, PWR-001 and W4C-F1 choices and W4C-F5 item; `EMCON.md` section 4b; EQ-25 |
| `w4c/readings/before-main-91894cd7/b-check_contracts_d.verdict.json` | `d970eba3cc89d21f5d166ca9db6dd5a9e9450ce4c83ed36477a7a1c94b4a8821` | 2438 | `fnd/w4c` `drafts/w4c/readings/before-main-91894cd7/b-check_contracts_d.verdict.json` | the w4c commit; the registry's EQ-25, PWR-001 and W4C-F1 choices and W4C-F5 item; `EMCON.md` section 4b; EQ-25 |
| `w4c/readings/before-main-91894cd7/b-check_contracts_e.verdict.json` | `b818e022d5e1528d3c017c27588bae1dad6a4c0171923d570c67e3fd1214b18a` | 2165 | `fnd/w4c` `drafts/w4c/readings/before-main-91894cd7/b-check_contracts_e.verdict.json` | the w4c commit; the registry's EQ-25, PWR-001 and W4C-F1 choices and W4C-F5 item; `EMCON.md` section 4b; EQ-25 |
| `w4c/readings/before-main-91894cd7/b-check_contracts_p.verdict.json` | `ada2a103d8e4dca6d9419949c912b86eb9152969828339fe15de0838ad4af2f6` | 1906 | `fnd/w4c` `drafts/w4c/readings/before-main-91894cd7/b-check_contracts_p.verdict.json` | the w4c commit; the registry's EQ-25, PWR-001 and W4C-F1 choices and W4C-F5 item; `EMCON.md` section 4b; EQ-25 |
| `w4c/readings/before-main-91894cd7/b-clock_check.verdict.json` | `1a481e6aa82582da443eb188fbcb0bc6451a16ebba5f6d32810dc653570ca73b` | 1221 | `fnd/w4c` `drafts/w4c/readings/before-main-91894cd7/b-clock_check.verdict.json` | the w4c commit; the registry's EQ-25, PWR-001 and W4C-F1 choices and W4C-F5 item; `EMCON.md` section 4b; EQ-25 |
| `w4c/readings/before-main-91894cd7/b-derate.verdict.json` | `ecd1cd3b1572450d2ab7f7912a8789867a815fb5808ea829be1d74f5d0e3adac` | 1256 | `fnd/w4c` `drafts/w4c/readings/before-main-91894cd7/b-derate.verdict.json` | the w4c commit; the registry's EQ-25, PWR-001 and W4C-F1 choices and W4C-F5 item; `EMCON.md` section 4b; EQ-25 |
| `w4c/readings/before-main-91894cd7/b-edge_length.verdict.json` | `a8b2708ff02e2ded01d6aae2844e44f4e7d6b32596caaab018c046bfe8160fe9` | 27360 | `fnd/w4c` `drafts/w4c/readings/before-main-91894cd7/b-edge_length.verdict.json` | the w4c commit; the registry's EQ-25, PWR-001 and W4C-F1 choices and W4C-F5 item; `EMCON.md` section 4b; EQ-25 |
| `w4c/readings/before-main-91894cd7/b-energy_chain.verdict.json` | `09605c98c9f6894c2a1a3926f252123826b538b17f53a06fc8b7aead9ff821bb` | 2479 | `fnd/w4c` `drafts/w4c/readings/before-main-91894cd7/b-energy_chain.verdict.json` | the w4c commit; the registry's EQ-25, PWR-001 and W4C-F1 choices and W4C-F5 item; `EMCON.md` section 4b; EQ-25 |
| `w4c/readings/before-main-91894cd7/b-energy_chain_a.verdict.json` | `d69111cfe222c13a67da7738f2864823246e55e70927abf7381a140197660b81` | 1750 | `fnd/w4c` `drafts/w4c/readings/before-main-91894cd7/b-energy_chain_a.verdict.json` | the w4c commit; the registry's EQ-25, PWR-001 and W4C-F1 choices and W4C-F5 item; `EMCON.md` section 4b; EQ-25 |
| `w4c/readings/before-main-91894cd7/b-energy_chain_b.verdict.json` | `6eebbf419c7db6c7d459bcedbdae2372f6cae890d6255ac4d4459e48e3643b1d` | 1612 | `fnd/w4c` `drafts/w4c/readings/before-main-91894cd7/b-energy_chain_b.verdict.json` | the w4c commit; the registry's EQ-25, PWR-001 and W4C-F1 choices and W4C-F5 item; `EMCON.md` section 4b; EQ-25 |
| `w4c/readings/before-main-91894cd7/b-energy_chain_e.verdict.json` | `c222e6fefb233d2892509d9fd4fbbe677e322ef3fec70b3639da880deedce36a` | 1750 | `fnd/w4c` `drafts/w4c/readings/before-main-91894cd7/b-energy_chain_e.verdict.json` | the w4c commit; the registry's EQ-25, PWR-001 and W4C-F1 choices and W4C-F5 item; `EMCON.md` section 4b; EQ-25 |
| `w4c/readings/before-main-91894cd7/b-energy_chain_e5.verdict.json` | `b59953058cbd1e2692215ef47a8d512672e608d1de531c82f29430bf773caf9e` | 1558 | `fnd/w4c` `drafts/w4c/readings/before-main-91894cd7/b-energy_chain_e5.verdict.json` | the w4c commit; the registry's EQ-25, PWR-001 and W4C-F1 choices and W4C-F5 item; `EMCON.md` section 4b; EQ-25 |
| `w4c/readings/before-main-91894cd7/b-energy_chain_p.verdict.json` | `9894d0e661f29ba65f7ea8fd139c9fed6a0d74788fd2d76e1b8863859a513b7c` | 1606 | `fnd/w4c` `drafts/w4c/readings/before-main-91894cd7/b-energy_chain_p.verdict.json` | the w4c commit; the registry's EQ-25, PWR-001 and W4C-F1 choices and W4C-F5 item; `EMCON.md` section 4b; EQ-25 |
| `w4c/readings/before-main-91894cd7/b-erc_gate.verdict.json` | `8d8e69545a4ac825e804d6860a5333435d2ce67c8da92aa04b4e4579aac65ec4` | 1855 | `fnd/w4c` `drafts/w4c/readings/before-main-91894cd7/b-erc_gate.verdict.json` | the w4c commit; the registry's EQ-25, PWR-001 and W4C-F1 choices and W4C-F5 item; `EMCON.md` section 4b; EQ-25 |
| `w4c/readings/before-main-91894cd7/b-inhibit_chain_a.verdict.json` | `94027079b05341da3e355ff93ccd5923f8f6cafd238e12d8be72bd42c37ad627` | 3995 | `fnd/w4c` `drafts/w4c/readings/before-main-91894cd7/b-inhibit_chain_a.verdict.json` | the w4c commit; the registry's EQ-25, PWR-001 and W4C-F1 choices and W4C-F5 item; `EMCON.md` section 4b; EQ-25 |
| `w4c/readings/before-main-91894cd7/b-inhibit_chain_b.verdict.json` | `91b19182f164c8f2cfdffc7d059f5d7f830f8153ae0546a0dec9b00fd0eb98ae` | 4928 | `fnd/w4c` `drafts/w4c/readings/before-main-91894cd7/b-inhibit_chain_b.verdict.json` | the w4c commit; the registry's EQ-25, PWR-001 and W4C-F1 choices and W4C-F5 item; `EMCON.md` section 4b; EQ-25 |
| `w4c/readings/before-main-91894cd7/b-inhibit_chain_c.verdict.json` | `513a6e8cd3294a64b867b66ed3a69496a571bc901ef08c7715680ff91245d248` | 3424 | `fnd/w4c` `drafts/w4c/readings/before-main-91894cd7/b-inhibit_chain_c.verdict.json` | the w4c commit; the registry's EQ-25, PWR-001 and W4C-F1 choices and W4C-F5 item; `EMCON.md` section 4b; EQ-25 |
| `w4c/readings/before-main-91894cd7/b-inhibit_chain_d.verdict.json` | `2a35db36b0b537e383800c5a4bc83f73c306ed2ee06665a0f5945dddd0a98384` | 3498 | `fnd/w4c` `drafts/w4c/readings/before-main-91894cd7/b-inhibit_chain_d.verdict.json` | the w4c commit; the registry's EQ-25, PWR-001 and W4C-F1 choices and W4C-F5 item; `EMCON.md` section 4b; EQ-25 |
| `w4c/readings/before-main-91894cd7/b-inhibit_chain_e.verdict.json` | `ba217963a3c0563ee0b2d00a2f7cda043ed1c6ffbc5e7997161a3e1e6bdf0bdd` | 2901 | `fnd/w4c` `drafts/w4c/readings/before-main-91894cd7/b-inhibit_chain_e.verdict.json` | the w4c commit; the registry's EQ-25, PWR-001 and W4C-F1 choices and W4C-F5 item; `EMCON.md` section 4b; EQ-25 |
| `w4c/readings/before-main-91894cd7/b-inhibit_chain_p.verdict.json` | `ff55d6a8a7d60f1863d8e91d9a8fdae3821dced9bbd790aaf1c91098f2675851` | 2644 | `fnd/w4c` `drafts/w4c/readings/before-main-91894cd7/b-inhibit_chain_p.verdict.json` | the w4c commit; the registry's EQ-25, PWR-001 and W4C-F1 choices and W4C-F5 item; `EMCON.md` section 4b; EQ-25 |
| `w4c/readings/before-main-91894cd7/b-intent_rails.verdict.json` | `7d4ea346eff194b94432c0bc80f9b6a2d39e369657ec1113ca83cd1c8b2e34a9` | 11415 | `fnd/w4c` `drafts/w4c/readings/before-main-91894cd7/b-intent_rails.verdict.json` | the w4c commit; the registry's EQ-25, PWR-001 and W4C-F1 choices and W4C-F5 item; `EMCON.md` section 4b; EQ-25 |
| `w4c/readings/before-main-91894cd7/b-interfaces.verdict.json` | `d37afeeaea27bd9c0c4476a2e68aa3c24dc5bc0441c0d0df7942ea0c764e5640` | 1458 | `fnd/w4c` `drafts/w4c/readings/before-main-91894cd7/b-interfaces.verdict.json` | the w4c commit; the registry's EQ-25, PWR-001 and W4C-F1 choices and W4C-F5 item; `EMCON.md` section 4b; EQ-25 |
| `w4c/readings/before-main-91894cd7/b-interfaces_a.verdict.json` | `006321ad7d5c7a6e8234242e173b872790fef26fc67aa181f724c3be4b27b7d0` | 1627 | `fnd/w4c` `drafts/w4c/readings/before-main-91894cd7/b-interfaces_a.verdict.json` | the w4c commit; the registry's EQ-25, PWR-001 and W4C-F1 choices and W4C-F5 item; `EMCON.md` section 4b; EQ-25 |
| `w4c/readings/before-main-91894cd7/b-interfaces_b.verdict.json` | `a6f9b1516e4c409eb1290328a2a728348f59d2fe3e6ee3876d4dcf043c5607a2` | 1635 | `fnd/w4c` `drafts/w4c/readings/before-main-91894cd7/b-interfaces_b.verdict.json` | the w4c commit; the registry's EQ-25, PWR-001 and W4C-F1 choices and W4C-F5 item; `EMCON.md` section 4b; EQ-25 |
| `w4c/readings/before-main-91894cd7/b-interfaces_c.verdict.json` | `4a47d204ee836f3842b125fcdc320b80cf599de113a471d57d99be8ff4a25f3c` | 1633 | `fnd/w4c` `drafts/w4c/readings/before-main-91894cd7/b-interfaces_c.verdict.json` | the w4c commit; the registry's EQ-25, PWR-001 and W4C-F1 choices and W4C-F5 item; `EMCON.md` section 4b; EQ-25 |
| `w4c/readings/before-main-91894cd7/b-interfaces_d.verdict.json` | `032a08382b1bcffac12fae5db9e07d550bb3443a7e70f63f87726d1977778d0e` | 1621 | `fnd/w4c` `drafts/w4c/readings/before-main-91894cd7/b-interfaces_d.verdict.json` | the w4c commit; the registry's EQ-25, PWR-001 and W4C-F1 choices and W4C-F5 item; `EMCON.md` section 4b; EQ-25 |
| `w4c/readings/before-main-91894cd7/b-interfaces_e.verdict.json` | `33556dc2c64de7ea35eeae7d298678ec5e597f08713cde6900fe45837916bd8d` | 1625 | `fnd/w4c` `drafts/w4c/readings/before-main-91894cd7/b-interfaces_e.verdict.json` | the w4c commit; the registry's EQ-25, PWR-001 and W4C-F1 choices and W4C-F5 item; `EMCON.md` section 4b; EQ-25 |
| `w4c/readings/before-main-91894cd7/b-interfaces_e5.verdict.json` | `7d52b4d5ac5e25255e11d9bf3b22f189933471b9550b949173016314ef6b29b5` | 1802 | `fnd/w4c` `drafts/w4c/readings/before-main-91894cd7/b-interfaces_e5.verdict.json` | the w4c commit; the registry's EQ-25, PWR-001 and W4C-F1 choices and W4C-F5 item; `EMCON.md` section 4b; EQ-25 |
| `w4c/readings/before-main-91894cd7/b-interfaces_p.verdict.json` | `b357a265e759739e632d84f6d0cda954af400f0f4ed7a96b26be9da2b0aef325` | 1621 | `fnd/w4c` `drafts/w4c/readings/before-main-91894cd7/b-interfaces_p.verdict.json` | the w4c commit; the registry's EQ-25, PWR-001 and W4C-F1 choices and W4C-F5 item; `EMCON.md` section 4b; EQ-25 |
| `w4c/readings/before-main-91894cd7/b-pin_map_lands_b.verdict.json` | `f266c5dfd235c744ab764af3c3f33907dd4bdc3130e12fe3710fcb526d410e4c` | 1254 | `fnd/w4c` `drafts/w4c/readings/before-main-91894cd7/b-pin_map_lands_b.verdict.json` | the w4c commit; the registry's EQ-25, PWR-001 and W4C-F1 choices and W4C-F5 item; `EMCON.md` section 4b; EQ-25 |
| `w4c/readings/before-main-91894cd7/b-port_protect.verdict.json` | `be960ab13ea4139b79fac8f85d182c58bb6e5d8f218c045bfe656344690dd3a6` | 1683 | `fnd/w4c` `drafts/w4c/readings/before-main-91894cd7/b-port_protect.verdict.json` | the w4c commit; the registry's EQ-25, PWR-001 and W4C-F1 choices and W4C-F5 item; `EMCON.md` section 4b; EQ-25 |
| `w4c/readings/before-main-91894cd7/b-port_protect_b.verdict.json` | `ea57953693e677d48c57a3deae106c392b59061f49277d11f3b3cac373a267f8` | 1762 | `fnd/w4c` `drafts/w4c/readings/before-main-91894cd7/b-port_protect_b.verdict.json` | the w4c commit; the registry's EQ-25, PWR-001 and W4C-F1 choices and W4C-F5 item; `EMCON.md` section 4b; EQ-25 |
| `w4c/readings/before-main-91894cd7/b-power_sequence.verdict.json` | `4dccfb70acc726db1eee179b8efbe0fd62a69a8b5ba7e38bd972d83b5a8d796d` | 1703 | `fnd/w4c` `drafts/w4c/readings/before-main-91894cd7/b-power_sequence.verdict.json` | the w4c commit; the registry's EQ-25, PWR-001 and W4C-F1 choices and W4C-F5 item; `EMCON.md` section 4b; EQ-25 |
| `w4c/readings/before-main-91894cd7/b-safe_lines.verdict.json` | `f2c5f0bab7be18a9fc4224b71f9e12bea1cf12fe9a57230ca758b7a8d6ee4faa` | 2426 | `fnd/w4c` `drafts/w4c/readings/before-main-91894cd7/b-safe_lines.verdict.json` | the w4c commit; the registry's EQ-25, PWR-001 and W4C-F1 choices and W4C-F5 item; `EMCON.md` section 4b; EQ-25 |
| `w4c/readings/before-main-91894cd7/b-safe_lines_b.verdict.json` | `bb36dace69de669c3d16b3a2498d9bde0ec6a04e76100bff7cd6d58f5bf5c0fe` | 2428 | `fnd/w4c` `drafts/w4c/readings/before-main-91894cd7/b-safe_lines_b.verdict.json` | the w4c commit; the registry's EQ-25, PWR-001 and W4C-F1 choices and W4C-F5 item; `EMCON.md` section 4b; EQ-25 |
| `w4c/readings/before-main-91894cd7/c-check_contracts.verdict.json` | `fd33b1cd0fe69dadf40885daec1f1a9cde80a5c0bc4c9aa0d8b2836d0fb6dde6` | 2941 | `fnd/w4c` `drafts/w4c/readings/before-main-91894cd7/c-check_contracts.verdict.json` | the w4c commit; the registry's EQ-25, PWR-001 and W4C-F1 choices and W4C-F5 item; `EMCON.md` section 4b; EQ-25 |
| `w4c/readings/before-main-91894cd7/c-check_contracts_a.verdict.json` | `0fcf5e06357f5656ddac7de1a4c076fe146da25f95b516628fc57bdaf495ad38` | 2693 | `fnd/w4c` `drafts/w4c/readings/before-main-91894cd7/c-check_contracts_a.verdict.json` | the w4c commit; the registry's EQ-25, PWR-001 and W4C-F1 choices and W4C-F5 item; `EMCON.md` section 4b; EQ-25 |
| `w4c/readings/before-main-91894cd7/c-check_contracts_b.verdict.json` | `6e6eceb2a286ba688f238c8f54ec2c883b0b5c4e5917cd5d895c86e90900eb46` | 2438 | `fnd/w4c` `drafts/w4c/readings/before-main-91894cd7/c-check_contracts_b.verdict.json` | the w4c commit; the registry's EQ-25, PWR-001 and W4C-F1 choices and W4C-F5 item; `EMCON.md` section 4b; EQ-25 |
| `w4c/readings/before-main-91894cd7/c-check_contracts_c.verdict.json` | `b77e98e097a9c79eb6b388b2e54459f99ed726595f5c672a0763867db4ca83ae` | 2436 | `fnd/w4c` `drafts/w4c/readings/before-main-91894cd7/c-check_contracts_c.verdict.json` | the w4c commit; the registry's EQ-25, PWR-001 and W4C-F1 choices and W4C-F5 item; `EMCON.md` section 4b; EQ-25 |
| `w4c/readings/before-main-91894cd7/c-check_contracts_d.verdict.json` | `d55a2f49cca065fd28386b3f80d3b63f05f8435eee90905a702ff20be4292ed1` | 2438 | `fnd/w4c` `drafts/w4c/readings/before-main-91894cd7/c-check_contracts_d.verdict.json` | the w4c commit; the registry's EQ-25, PWR-001 and W4C-F1 choices and W4C-F5 item; `EMCON.md` section 4b; EQ-25 |
| `w4c/readings/before-main-91894cd7/c-check_contracts_e.verdict.json` | `e7d79b812cbd97188e925475e04a300b480ab548b38494ccec5975fb28a9761d` | 2165 | `fnd/w4c` `drafts/w4c/readings/before-main-91894cd7/c-check_contracts_e.verdict.json` | the w4c commit; the registry's EQ-25, PWR-001 and W4C-F1 choices and W4C-F5 item; `EMCON.md` section 4b; EQ-25 |
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
