meshsat/meshsat-fieldkit/v2/ecad/easyeda-pro/README.md

# EasyEDA Pro imports of the V2 carrier boards

KiCad 9 is the source of every V2 board (`v2/ecad/pcb-*` and the generators in `v2/ecad/tools/`). The archives here are one-way imports into EasyEDA Pro, first made on 8 Sep 2026 for the cooperation with EasyEDA and JLCPCB (MESHSAT-776). Nothing is edited on the site and nothing here feeds back into the KiCad sources; when a board is regenerated it needs a fresh archive.

**REBUILT 13 September 2026 for an outside review.** `tools/easyeda_import_set.py` builds the archives for whatever the tree holds, so the set is a rebuild rather than a one-off: **A24, B19, C10, D10, E7, E5, P3**, in `import/`. The September archives and site exports are kept beside them as the record of that generation (A22, B16, C7, D8, E6, E5, P2), and every one of those describes a board we are no longer building.

Every project on the site is Private on the shared JLCPCB login (Personal workspace), none is published on OSHWLab, and no order is placed from them.

## Boards

| Board | Revision | Source snapshot | Site project | Layers | State |
|---|---|---|---|---|---|
| PCB-A power | A22 | `v2/release/revA/boards/meshsat-pcb-a-revA-A22` | MeshSat V2 A A22 | 6 | routed, released |
| PCB-B compute | B16 | `v2/release/revA/boards/meshsat-pcb-b-revA-B16-quote` plus the working-folder schematic | MeshSat V2 B B16 | 6 | placed, unrouted, quote only (held on this placement, B17 follows) |
| PCB-C display | C7 | `v2/release/revA/boards/meshsat-pcb-c-revA-C7` | MeshSat V2 C C7 | 4 | routed, released |
| PCB-D APRS | D8 | `v2/release/revA/boards/meshsat-pcb-d-revA-D8` | MeshSat V2 D D8 | 4 | routed, released |
| PCB-E1 dock | E6 | `v2/release/revA/boards/meshsat-pcb-e-revA-E6` | MeshSat V2 E1 E6 | 4 | routed, released |
| PCB-E5 block | E5 | `v2/release/revA/boards/meshsat-pcb-e5-revA-E5` | MeshSat V2 E5 E5 | 2 | routed, released, PCB only (no schematic by design) |
| PCB-P pack | P2 | `v2/release/revA/boards/meshsat-pcb-p-revA-P2` | MeshSat V2 P P2 | 2 | routed, released |

The site projects are named "MeshSat V2 <board> <rev>"; by owner instruction nothing on the site (project names, introductions, file names) refers to the source tool.

## Folders

- `import/<board>-<rev>-import.zip`: the archive that was uploaded, built from the deliverable snapshot: `<project>.kicad_pro`, `.kicad_sch`, `.kicad_pcb`, `fp-lib-table` and the `meshsat.pretty` footprints the snapshot carries (the B16 quote snapshot has no schematic and no footprint library, so its archive takes the working-folder schematic and the shared `v2/ecad/meshsat.pretty`).
- `<board>-<rev>/`: the exports of that project: `MeshSat-V2-<x>-<rev>.epro2` (Project Save as (Local), EasyEDA Pro V3 format), `MeshSat-V2-<x>-<rev>-schematic.pdf` (File > Export > PDF, merged sheet; none for E5), `<board>-<rev>-pcb-view.jpg` (2D editor), `<board>-<rev>-3d-view.jpg` (3D view), and `import-notes.txt` with the project id, the importer log, the checks made and every warning.

## How an import is made (EasyEDA Pro V3.2.148, web editor)

1. Build the archive from the deliverable snapshot (not from the working folder): project, schematic, board, `fp-lib-table`, the snapshot's `meshsat.pretty`; name it `<board>-<rev>-import.zip` under `import/`.
2. In the editor, Start Page > Import KiCad (or File > Import), accept the notice, choose the zip, Import Document, system theme, associate footprint and 3D model automatically. In the Import Document dialog set Operation New Project, Owner Personal, Project "MeshSat V2 <board> <rev>", a one-line introduction, then Import.
3. Read the Log tab: the import step reports "Import project success" or "import failed"; warnings there (footprints moved between layers, unbound 3D models) go into `import-notes.txt`.
4. Open the PCB document and check the layer panel (copper count against the source), the outline, the footprints and the 3D view; open the schematic.
5. Export: File > Save as > Project Save as (Local) (epro2), File > Export > PDF on the schematic (Default theme, Original Size, All, Merged sheet), and a screenshot of the 2D and the 3D view; move the files into `<board>-<rev>/`.
6. Confirm on `u.easyeda.com/account/user/projects/all` that the project carries the Private tag.

## Findings of the first import (8 Sep 2026)

- Every import completed with all footprints placed and the copper intact; no missing-footprint message on any board. C7 reported four toggle-switch footprints moved to the bottom layer (see its notes).
- No 3D model is bound to any part ("N components were not generated in 3D"): the sources ship no model files, which is expected.
- The stackup does not carry over (the 3D property panel shows placeholder thicknesses); the JLC04161H-7628 and JLC06161H-3313 stackups of the boards are ordered on the JLCPCB cart lines, not read from these projects.
- The schematic arrives as one merged sheet; DRC was not run and design rules were not compared.
- The site's upload is flaky: B16 failed twice ("The upload of the project log failed!", "Network Error!") before the same archive imported on the third attempt after an editor reload; C7 and D8 each needed one retry. A failed import leaves an empty project shell under the chosen name, which has to be deleted on the projects page before the retry. Nothing about the archives caused the failures.

## Gerber exports (8 Sep 2026)

Per project, Export > PCB Fabrication File (Gerber) with One Key Export (the JLCPCB default set), saved as `<board>-<rev>/MeshSat-V2-<x>-<rev>-gerber.zip`. The six routed boards export cleanly. B16 is placed and unrouted, so its zip is named `MeshSat-V2-B-B16-gerber-UNROUTED-quote-only.zip` and is not a manufacturable set (the exporter warns about incomplete connections; the export was continued for the record). Each zip holds the copper layers of the board, both solder masks, both silkscreens, the outline, three drill files, paste and assembly layers; the files inside are named `Gerber_<layer>` and `Drill_<type>` only.

## Provenance strings in component descriptions (not cleaned, by owner ruling 8 Sep 2026 15:00)

The project-library symbols `Connector_Generic_Conn_NNxNN` carry the source library's provenance in their Description attribute ("..., script generated (kicad-library-utils/schlib/autogen/connector/)"; 56 symbols across A22, B16, C7, D8, E6 and P2, none in E5). They are not in the Gerbers or the schematic PDFs, and the projects are Private. Editing them on the site by hand is not worth the clicks (the editor's Find and Replace, the device editor and the extension API all leave that attribute alone); if the projects are ever published, the fix is one scripted pass over the exported `.epro2` files, or a correction in the source libraries before a fresh import. Details in `pcb-b-compute-B16/import-notes.txt`.

## Cart of the same day

The JLCPCB quote cart of this set (13 lines, all ticked: merchandise 4594.90 EUR, estimated shipping 129.22 EUR, subtotal 4724.11 EUR, nothing paid) is recorded in `v2/release/revA/order/ORDER-LOG.md` section 5.1 with the screenshot `v2/release/revA/order/cart-830-set-2026-09-08.jpg`.

## Rebuild for the review, 13 September 2026

The 12 September reviewer works in EasyEDA, and every project of the September set was a generation behind, so
`tools/easyeda_import_set.py` rebuilt the archives from the current tree. It is a tool rather than a procedure
because this will happen again on the next regeneration.

| Board | Revision | Built from | State of that board |
|---|---|---|---|
| PCB-A power | A24 | deliverable `meshsat-pcb-a-revA-A24` | routed and cut, 0 hard, 0 unrouted; eight of twelve rails over IPC current density |
| PCB-B compute | B19 | phase directory `pcb-b-compute-b19` | **not routed**, hard 30 and 499 unrouted after the pair pass, hard 0 placed underneath |
| PCB-C backer | C10 | phase directory `pcb-c-display-c8` | routed, not cut, 0 hard and 1 unrouted, to be read as two |
| PCB-D APRS | D10 | deliverable `meshsat-pcb-d-revA-D10` | routed and cut, 0 hard, 0 unrouted; its 5 V rail's width is under review |
| PCB-E1 dock | E7 | deliverable `meshsat-pcb-e-revA-E7` | routed and cut, 0 hard, 0 unrouted; both rails over IPC current density |
| PCB-E5 block | E5 | deliverable `meshsat-pcb-e5-revA-E5` | routed and cut, nothing open, no schematic by design |
| PCB-P pack | P3 | deliverable `meshsat-pcb-p-revA-P3` | routed and cut, 0 hard, 0 unrouted; two of three rails over IPC current density |

**The source rule, kept from September:** the archive comes from the DELIVERABLE snapshot where one exists, so
what a reviewer opens is the same copper the gerbers were cut from. A board with no deliverable yet comes from
its phase directory and its note says so.

**Every archive carries `<stem>/IMPORT-NOTE.txt`** with that board's measured state, how to import it, and what
the import is not. Handing someone a board without its numbers invites them to assume it is finished, and two
of these seven are not.

**Nothing here has been uploaded to the site.** The September generation was imported on the shared JLCPCB
login; this one is archives only, for a reviewer to import into his own account. The runner does not log in
anywhere, which is a standing rule of this project and not a limitation of the format.
