meshsat/meshsat-fieldkit/v2/images/concept-1450/set-ten/README.md

# The kit assembled: eighteen views, set ten, rendered 15 September 2026

A concept model of the MeshSat field kit V2 in a Peli 1450 with its 1450PF frame: the seven carrier boards as exported from their KiCad files (A32, B19 placed, C17, D11, E9, E5, P4), the makers' STEP models where the project holds them, and stand-in shapes for the rest. **Prototype design, nothing built.** Rulers in mm, 10 mm ticks, numerals every 50; the floor grid is 50 mm.

**The monitor (Xenarc 709GNK) sits IN the 3 mm aluminium face plate with its glass level with the plate's top face**, 0 mm proud in the model; the project holds it to 1 mm at most. The sets before this one (set eight and earlier) showed it 28.7 mm proud, which was a scene defect corrected on 9 September; those images are superseded.

| file | view |
|---|---|
| `01-assembly-1-closed.png` | the case closed |
| `02-assembly-2-lid-open.png` | lid open: the face plate as the operator sees it |
| `03-assembly-3-plate-off.png` | the face plate lifted off |
| `04-assembly-4-stack-out.png` | the A and B stack lifted out on its rods |
| `05-assembly-5-dock.png` | the dock strip on the case floor |
| `06-az135-el40-open-nocables.png` | open, from the back-left, no cables drawn |
| `07-top-face.png` | the face plate straight down |
| `08-face-detail-left.png` | the face plate, left half, close |
| `09-face-detail-right.png` | the face plate, right half, close |
| `10-face-underside.png` | the underside of the face plate with the backer ring |
| `11-stack-no-face-top.png` | the stack from above without the face |
| `12-cutaway.png` | a cutaway through the case |
| `13-lid-inside.png` | the lid inside with its bracket |
| `14-connector-plate.png` | the connector plate on the back wall |
| `15-east-wall.png` | the east end wall and its jacks |
| `16-west-wall.png` | the west end wall, the pack side |
| `17-dock-joint.png` | the blind-mate joint at the dock |
| `18-antennas-az045.png` | the antennas fitted, from the front-right |

Set ten (15 September 2026, evening): the same eighteen views with the display screenshot visible on the glass in every view (the screen object sat inside the glass slab in sets eight and nine and rendered as dark refracting glass) and the monitor rear block under the plate, where it belongs. Rendered on a rented RTX 4090 in nine minutes. Prototype design, nothing built.
