meshsat/meshsat-fieldkit/v2/docs/records/l4e11/README.md

**ROUND 17 (P0 Slot C, branch `fnd/p0t10` from `fnd/p0base` `e132db0e`, 5 October 2026): DONE: the check V6's V6-m2, DD-7's netlist check restated for record l8p's thermal guard (the LOOP group: RT1 or the guard's pair) and 20c and 20f restated with the guard's pulled level, its 30 uA and C261 (out 27, page 27); test_l4e11 composes the guard and its mutations fail. NOT DONE: no independent check of round 17. NEXT: record l8p's copy of this record taken again at this round.**

# L4-E11: source-only and dead-pack operation, the vehicle-entry interconnect and the hot swap's fault timer (MESHSAT-1357)

**ROUND 16 (the check V2RG, branch `fnd/l4e11r11`, 5 October 2026): DONE on the desk. What is done: V2RG found round 15's guard NOT CLOSED (V2RG-B1), the second negative check of the lead treatment, so that design loop ENDED; by the coordinator's diagnosis the lead heat is now an EXTERNAL QUALIFICATION: the net heat at each heating lead's joint at most 10 mW a lead in calibration, heating and sensing, a requirement on the supplier's fixture that the supplier demonstrates on it before any coupon run (step 0: a measured residual by three thermocouples, or a reference coupon of known impedance), V8 judging the measured residual; its bound, of either sign, carried through the reduction (it enters line 2 5.51 times a reading's, the direct line once); the design target restated for it (Zw at most 37.59 K/W, Zself 30.07 for three side by side at m 0.1, R17 at most 0.294 K/W, the pours 0.1 mOhm) with the verdict table (the target passes at every edge, 0.1 K and 1 K over the limit fail at every edge); V2RG-m1 to m6 answered; `v2/docs/test-procedures/TP-E11-29.md` rewritten on them. What is not done: nothing bought, built or measured; **V2RG-B1 stays OPEN as a supplier qualification item** until the supplier's demonstration shows the requirement met; the minors are the coordinator's to verify (clerical); TP-E11-29 stays NOT EXECUTABLE until L4-E9 restates R-159 and a supplier agrees in writing, and it is **ready to be PUT to a supplier for that agreement**, with the fixture requirement as the supplier's scope. Next action: L4-E9 restates R-159 from E11-29's row; the procedure goes to a supplier for agreement; the supplier's step 0.** Case row C-PROT rev 1. Tests `t_round16_*`; the line below the table. The round is the author's own work: UNVERIFIED.

V2RG answered (the check as received: `_runs/claude/inputs-20261004e/CHECK-V2RG-AS-RECEIVED.md`, an AI review of `fnd/l4e11r11` at `ba5862ab`; the coordinator's diagnosis `_runs/claude/l4e11r16/DIAGNOSIS.md`; filing both is the integrator's):

| Finding | What changed | File |
|---|---|---|
| **V2RG-B1** (blocking; the lead treatment's second negative check: the loop ENDS) | Round 15's guard **withdrawn as the qualification** (holding two thermocouples equal across a heated span does not null the joint's heat flow; V2RG's model 31 to 426 mW a lead at a 0.05 m guard against round 15's 14.9 mW; round 15's V8 judged the controller, not the heat flow); it stays as construction guidance. **The fixture requirement (SESSION, the supplier's scope):** the net heat at each heating lead's joint at most **10 mW a lead** in every state, its measurement's uncertainty included; **the supplier's demonstration** on the actual fixture before any coupon run (step 0: three thermocouples on the lead's copper over an unheated span, k A (3 T0 - 4 Tmid + TL) / L, about 2.65 mW resolution at a 0.02 K match over 60 mm; or a reference coupon of known thermal impedance), its instruments kept for the runs; **V8 restated** as a check of that measured residual. **The allowance's cost:** each reading may carry (2 leads) x 10 mW x Z_kJ of either sign (Z_kJ at its bound Zself for planning; a run reads its own by reciprocity); the bound is carried through the reduction and summed: it enters line 2 **5.51 times** a reading's and the direct line once. **The target restated:** Zw at most 37.59 K/W (trade: 0 mW 42.24, 5 mW 39.77, 10 mW 37.59, 20 mW 35.27, 30 mW 31.56 K/W); at it line 2 62.27 K, U 2.42 K, the leads' bound 3.32 K; the direct line U 1.94 K, its bound 0.6 K. **The verdict table:** the target passes at every edge (readings at +-U, the leads at their bound of either sign); 0.1 K and 1 K over the limit fail at every edge; counting the bound once in line 2 would pass the 1 K over coupon (a test). Two levers relax the target (a run's own Z_kJ; a supplier correcting each reading by its measured residual), neither adopted. **V2RG-B1 stays OPEN as a supplier qualification item** | `l4e11_power.py` (`R16_Q`, `R16_Q_SEL`, `r16_lead_bounds`, `fix26_round`), out and page 26a to 26d; block E11-29 (operating point, boundaries, uncertainty, design target, comparison rule); row E11-29 (`e11_29_method`); TP status, sections 2, 4 to 9, step 0, item 10, V8; `apply_gen_sch_a_charger.py` (its layout comment: Zw at most 37.59 K/W) |
| **V2RG-m1** | the page's row E11-29 is now the script's row word for word, the target as "Zw at most 37.59 K/W (Zself 30.07 K/W for three side by side at m 0.1)"; ten other rows whose page text missed a figure of the script's (E11-03, 04, 05, 07, 10, 13, 18, 21, 24, 28; none quoted by a procedure) restated from the script; a test reads every page row's figures against the script's and E11-29's whole | page section 8; `test_l4e11.py` |
| **V2RG-m2** | the direct line's U with the FETs' and R17's 1 % powers and the lot correction: 1.94 K at the restated target (1.88 K without them at the same reading) | out and page 26d, 26e; block; TP section 9 |
| **V2RG-m3** | a coupon exactly at the limit, lines 1 and R17 with room, passes 3 of 2,000 draws from the budget (0.15 %) on the record's own functions; round 15's "about 2.5 %" restated | out and page 26e; TP section 9 |
| **V2RG-m4** | the band supply's 23.93 A leads stand for the service's pack conductors: their cross-section, insulation, length and termination a recorded boundary of the comparison rule (SESSION) | block E11-29; TP item 10 |
| **V2RG-m5** | any heater on a lead driven by a floating DC supply or its drive held through each reading window, included in step 6's pickup check, the census and V3 | TP item 10, step 6 |
| **V2RG-m6** | 96.6 times the largest other conductor at 34.48 uA (965.5 uA against 10 uA); the test module's docstrings restated | TP item 5; `test_l4e11.py` |

Tests at this round, as `run.py` printed them: `test_l4e11 test_public_hygiene`: `tests: 85 passed, 0 failed, 0 skipped` (two new, `t_round16_*`). Run against round 15's procedure (`ba5862ab`) both fail ("the procedure does not state the lead heat as a requirement on the supplier's fixture" first). Changed expectations, each on V2RG's basis and the coordinator's diagnosis: round 15's guard test now refuses round 14's statements and reads the block's requirement instead of the guard; round 15's status and row assertions read V2RG-B1 OPEN and the requirement; the draft's target is round 16's. The procedures' quote verifier on TP-E11-29: every quote of this record matches (4 table, 15 text); the two failures it reports are L4-E9's cells, as before; set 29's fixture-test anchor still occurs once (the builder keeps it on one line). **For the integrator:** the charger draft's bytes changed again (its layout comment), so record l8p's copy and the pins are re-taken at integration; ten page rows of section 8 were restated from the script (none is quoted by a procedure).

**ROUND 15 (the final recheck V2RF, branch `fnd/l4e11r11`, 5 October 2026): DONE on the desk. What is done: V2RF's blocking finding V2RF-B1 corrected from the physics (round 14's heavy-lead check V8 and its lead term withdrawn; each heavy lead of the heating supply GUARDED by a heater held at zero gradient, which removes the leads from the network and leaves at most 14.9 mW a lead with its lagged lug), and the minors V2RF-m1 to m5 answered (the interlock on SW_S's own state, searched; the galvanic boundary, the census and V3 in the chamber; a solid-state SW_S with a clamp; each line's U propagated through the reduction; the pours' allowance in the design target and in the charger draft's layout requirement), in the record (section 25, out 25) and in `v2/docs/test-procedures/TP-E11-29.md`. What is not done: nothing bought, built or measured; the guard and the minors have had NO check (the coordinator's to schedule; a second negative on the guard ends that loop); the guard's, switch's, clamp's and budget's figures are SESSION proposals for the supplier's parts and instruments; TP-E11-29 stays NOT EXECUTABLE until R-159 is restated (L4-E9's) and a supplier agrees in writing. Next action: the targeted check of section 25 with TP-E11-29 (the guard, the design-target verdicts, the interlock search, the propagated U); then L4-E9 restates R-159 from E11-29's row.** Case row C-PROT rev 1. Tests `t_round15_*`; the line below the table. The round is the author's own work and has had no independent check: UNVERIFIED.

V2RF's findings answered (the final recheck as received: `_runs/claude/inputs-20261004e/CHECK-V2RF-AS-RECEIVED.md`, an AI review of `fnd/v2cand3` at `15842008`; filing it is the integrator's; its V2RF-m6 is record l8p's):

| Finding | What changed | File |
|---|---|---|
| **V2RF-B1** (blocking; fails safe): round 14's V8 and lead term cannot be met | Reproduced: a 4 mm2 lead's fin conductance 0.0153 to 0.0197 W/K, so V8's 30.3 mW holds only within 1.53 to 1.98 K of the lead; a joint 5 to 40 K over it draws 0.076 to 0.79 W; the term 2 x Zself x q costs 6.2 to 64.4 K a lead; the factor 2 becomes 8 for two leads coupled at 15 of 20 K/W; at the design target round 14's term reads line 2 at 85 to 180 K. **Two corrections compared:** (b) measuring the correction on passive leads leaves the pair's curvature bias, 11 to 150 mW a lead, and (I - F)^-1 to measure; **(a) SELECTED (SESSION): guard each lead**, a heater tape over the lug's barrel and the lead, held by an integral controller so the pair's difference reads zero, the lug and the tape lagged: at steady state the coupon is the coupon without its leads plus a residual of at most 14.9 mW a lead (the pair's 5.2 mW and the lagged lug's own 9.7 mW, which my own review of the first draft found missing), its effect at most Z_kJ times it (Z_kJ by reciprocity from the joint's thermocouple), 1.22 K for both at 40.78 K/W, 0.99 K at the target; **no factor and no assumption on the leads' share is needed** (so the half-share ASSUMPTION is not restated). V8 restated as the guard's control (in control, never at zero or full output, the logged difference within 0.05 K). **A coupon at the design target passes at every error edge within U, and one over the limit fails at every edge** (25g's table). Reversed by: a guard that cannot hold its lead on a supplier's fixture; then (b) | `l4e11_power.py` (`R15_LEAD`, `fix25_round`, `render_fix25`), out and page 25a, 25b, 25g; block E11-29 (operating point, boundaries, comparison rule); row E11-29 (`e11_29_method`); TP sections 2 to 9 |
| **V2RF-m1**: the interlock read a proxy | R1 to R6 on SW_S's OWN state (its drive enable, continuously), the shunt under 10 mA a second barrier; a search of every reachable state (`r15_states`): round 14's rules reach the clamp H1 and the open supply H2, round 15's reach none; each of R1 to R5 dropped alone reaches a hazard (R6 implied, kept); a failed-short SW_S leaves the pours at 0.112 V under the hot threshold, and V10 refuses the reading | out and page 25c; TP sections 3 to 6 |
| **V2RF-m2**: the galvanic boundary and V3's reach | the boundary stated (insulated thermocouples or channel-isolated logger, isolated sequencer, interlock and drives, one earth point); the census 34.48 uA, 3.45 % of the sense current with the thermocouples, guards, barriers, supplies to earth and the clamp; V3 repeated in the chamber with everything connected, before the cases and at once after the last | out and page 25d; TP sections 5, 6 and the V3 row |
| **V2RF-m3**: SW_S's opening | solid-state only (the relay dropped); a clamp across SW_S for 21 to 182 uJ a reading (a bidirectional TVS, 20 V standoff, 0.2 mJ repetitive, or a printed avalanche rating), ending the current in 0.7 us before the tie; its leakage in the census | out and page 25e; TP sections 4 and 6 |
| **V2RF-m4**: one U for every line | each line's U propagated through the reduction from the budget's sources (`r15_u`), absolute terms absolute and common terms common: at the target line 1 3.63 %, line 2 2.52 K (3.66 %), R17's line 0.353 K/W, a direct reading 1.96 K; the control run's difference applied as a correction (0.25 K left); a search with readings drawn from the budget (3,600 matrices: none accepted over 150 C; the claim restated to its model, about 2.5 % at the limit for a k = 2 rule) | out and page 25f; block E11-29; TP sections 6, 8 and 9 |
| **V2RF-m5**: E11-29's sizing target short of line 2 | the design target carries the pours' allowance (SELECTED 0.1 mOhm, the two pours' largest paths summed): each junction's Zw at most 41.51 K/W (three side by side at m 0.1: Zself 33.21, S 39.85 K/W), R17's coupling at most 0.294 K/W, so line 2 and R17's line pass with twice their U; the trade for 0 to 0.2 mOhm printed; the acceptance bars unchanged; the layout requirement in block E11-29 and in the charger draft's layout comment | out and page 25g; `apply_gen_sch_a_charger.py` (comment only); block E11-29 |

Tests at this round, as `run.py` printed them: `test_l4e11 test_public_hygiene`: `tests: 83 passed, 0 failed, 0 skipped` (three new, `t_round15_*`). Run against round 14's procedure (`08f7e38a`) all three fail ("the procedure's heavy leads are not guarded" first). Changed expectations, each on V2RF's basis: round 14's status test now reads V2RF's closure of the fixture and pass rules instead of "the independent recheck ... as a precondition" (the brief's preconditions are R-159 and the supplier); round 13's kept phrase "the independent check" stays true of the status text. The procedures' quote verifier on TP-E11-29: every quote of this record matches (4 table, 15 text in all); the two failures it reports are L4-E9's cells, older in this tree, as before. Set 29's fixture-test anchor "(Zself + 2 Zmut) at most 40.78 K/W steady" still occurs once. **For the integrator:** the charger draft's bytes changed (its layout comment only), so record l8p's copy of it (V2R's "four drafts byte for byte") and the records that pin it are re-taken or re-pinned at integration; record l8p's guard will name the copy. The page's dependency table (section 11) re-cites its record lines after this round's In short bullet.

**ROUND 14 (the independent recheck V2R, branch `fnd/l4e11r11`, 5 October 2026): DONE on the desk. What is done: V2R's two blocking findings on TP-E11-29 corrected from the arithmetic in the record (section 24, out 24) and in `v2/docs/test-procedures/TP-E11-29.md`: V2R-B1, the fixture redrawn so the heating supply is isolated by a series switch for every reading, each state's current paths searched and bounded on Nexperia's printed rows; V2R-B2, the pass lines restated junction by junction at each row's own worst split with the baseline judged in the limit's line, the rule proved by a search in `l4e11_power.py` that is also a test; the minors m1 and m3 to m7 answered. What is not done: nothing bought, built or measured; the corrections have had NO recheck (the coordinator's to schedule; a second negative on either ends that loop); the switch, lead and budget figures are SESSION proposals for the supplier's parts and instruments; TP-E11-29 stays NOT EXECUTABLE; the first prototype's gate links and depopulation are not drafted. Next action: the targeted recheck of section 24 with TP-E11-29 (fixture, sequence, lines 1 to 3, the search), then the limits agreed (R-159 restated from E11-29's row) and a supplier's agreement.** Case row C-PROT rev 1. Tests `t_round14_*`; at this round `test_l4e11` and `test_public_hygiene`: see the line below the table. The round is the author's own work and has had no independent check: UNVERIFIED.

V2R's findings answered (the recheck as received: `_runs/claude/inputs-20261004e/CHECK-V2R-AS-RECEIVED.md`, an AI review of `fnd/v2cand2` at `8ce0441e`; filing it is the integrator's):

| Finding | What changed | File |
|---|---|---|
| **V2R-B1** (blocking): the fixture never isolated the heating supply | Reproduced: the script holds each fixture as elements with the states in which each is closed and searches for a path joining the VBAT and CH_BATQ pours outside the FETs (`r14_state`): round 13's joins them in calibration and sensing through the supply's + lead, the bypass and the shunt (20 uV across the pours for the 1 mA against a 1.5 to 3 V threshold); its "or the supply is clamped" puts the heating current through a diode-connected FET (at least 20.7 W on the threshold's least printed row). **Redrawn (SESSION):** a series switch SW_S in the supply's + lead (blocking both polarities), the bypass SW_B onto a dummy leg on the supply's side of it, the gate tied at its own drain tap, a hardware interlock (a gate tied to its drain only with SW_S open); the sequence with its timing (SW_B closes, 10 us later SW_S opens, 2 us later the gate is tied, samples 100 us to 10 ms, then the reverse; the heating off 1 % of the time, powers averaged over the cycle); no state joins the pours. **The device under test alone, by margin:** in a reading every other conductor carries at most 28 uA, 2.8 % of the sense current (the off FETs 20 uA at 125 C and IGSS 0.1 uA, Nexperia BUK6Y10-30P 17 April 2020 Table 7 p.6; SW_S 1 uA, the drivers 6 uA, the digitiser 0.9 uA, PROPOSALS), 100 times the largest other; in heating the device carries 8.46 to 22.46 A and the rest at most 26.1 uA; the switch's leakage common to calibration and reading (outside the chamber), read before and after by V3; its on-resistance in no power (the shunt and taps inside it), in the supply's compliance (V7); the settling 34.8 us against the first sample at 100 us (typical Ciss, labelled). 23f's clamp withdrawn | `l4e11_power.py` (`R14_SW`, `R14_FIXTURES`, `r14_state`, `fix24_round`), out and page 24a, 24b, 23f; TP sections 3 to 7 |
| **V2R-B2** (blocking): two pass rules could pass a specimen over the limit | Reproduced: the fixed split reads 6.2, 15.6 and 22.1 % under the worst at m 0.25, 0.5 and 0.8; V2R's example passes every round 13 line at 152.3 C. **Restated (SESSION):** each junction at the exact worst split of its OWN row (`worst_row`: C_k the largest term, D_k the other two, Zw_k = 9 C_k^2 / (4 (2 C_k - D_k)) under m_k = D_k / (2 C_k) of 1/4, else C_k + D_k: S_k against 21b's bar at m_k, exactly; derived in 24d, checked against a scan of every split in the test); line 1 the FETs' allocation (45.88 K/W); **line 2 the limit itself**: the measured baseline B_k + R17's coupling x 2.86 W + 1.3448 W x Zw_k + the pours' and leads' bounds at most 73.75 K; line 3 the same read directly in cases F at each row's worst split; step 14's bar at the largest ratio WITHDRAWN. **The proof by search** (`r14_search`, four families of 20,000, readings perturbed within U): round 14 accepts none over 150 C, and with exact readings refuses none that meets the limit and both allocations; round 13's step 14 passes 2,043 over the FETs' allocation and its lines together 2,845 over 150 C (to 159.9 C); the record's own rule none. Selected over the record's rule as written because it is exact (the record's rule is safe and looser) | `l4e11_power.py` (`bar_at`, `worst_row`, `r14_lines`, `r13_step14`, `r11_record_rule`, `r13_direct`, `tj_exact`, `r14_matrix`, `r14_search`), out and page 24c to 24e; the row E11-29 (`e11_29_method`) and block E11-29; TP sections 6 and 8 |
| **V2R-m1** | 20g on 22c's set: 3.72 mA (the breaker restarted), 4.32 at SYSOVP, 6.45 at the clamp; the 2N7002 row 6.45 mA; 21d's "R256 6.8 kOhm" marked SUPERSEDED | `l4e11_power.py` (render of 20g), out and page 20g, page 21d |
| **V2R-m3** | gate k tied at tap Dk's own line, the reading V(tap Sk, tap Dk) its VGS (a tie 0.1 mOhm away adds 2.4 mV at 23.93 A); the pickup step subtracted, 0.1 K in the budget | page 24g, block E11-29, TP sections 4 to 6 |
| **V2R-m4** | the control run C0 (the gate driven as in a run, SW_S open, the coupon isothermal at the top temperature, read in the same window) bounds a bias-induced shift and the settling (V9); the early-time correction its own term; nine terms, 3.47 %; each line the reading plus the ACHIEVED U, the figures illustrations (39.41 K/W, 44.34 K/W, 71.28 K) | out and page 24f, block E11-29, row E11-29, TP sections 6, 8 and 9 |
| **V2R-m5** | the matrix is the rise over step 6's baseline | TP step 14, page 24d |
| **V2R-m6** | nothing else joins the pours (C236 and CELL_FUSED's 104 uF are 65.9 uF in series across the node: 1 mA moves it 3.03 V in 0.2 s); the first prototype is a specimen only with its gate links AND populated as the coupon is; on the coupon no capacitor, load or dummy on either pour, the dummies insulated, the band stopping at each pour's joint | block E11-29's specimen line, page 24g, TP sections 2 and 5 |
| **V2R-m7** | the heavy leads named (at least 4 mm2, joined where board A's current joins each pour, two thermocouples each: q = k A dT / dx, 0.39 K at 2 % of 1.513 W; V8) and their outgoing heat x twice Zself added to lines 2 and 3 (removing a lead changes the network: the factor 1 / (1 - g Z_jj) taken at 2, an ASSUMPTION); the pours' service loss, at most (23.93 A)^2 x the sum of the two pours' largest path resistances (each measured four-wire from its joint's tap) x Zself, added to line 2 (the heating cases carry 0.333 to 0.881 of it) | out and page 24f, block E11-29's boundaries, TP sections 5 and 6 |

The method's state after V2R: method (B) CONFIRMED AS CONDITIONAL as an electrical method by V2R (its conditions stand: the per-device K-factor, the off devices' leakage over 125 C, a recoverable bias-induced shift, a supplier's agreement, R-159 restated); the fixture and the pass rules CORRECTED here and UNVERIFIED. What the round leaves for others: **L4-E9**, R-159 still carries 45.88 K/W and no method, and 5d's Specimen cell still offers the first prototype (now also needing its depopulation, V2R-m6); **the integrator**, V1's, V2's and V2R's checks as received to file, and `tp_check.out` to regenerate after TP-E11-37's re-quote (round 13's note below stands); **board A's generator**, the gate links (not drafted).

Tests at this round, as `run.py` printed them: `test_l4e11 test_public_hygiene`: `tests: 80 passed, 0 failed, 0 skipped` (three new, `t_round14_*`; round 13's procedure test keeps the rule, the reading plus the achieved U, where it named the fixed 39.51 K/W, by V2R-m4). Run against round 13's procedure (`4def5975`), `t_round14_v2r_b1_*` fails ("the procedure's fixture does not isolate the heating supply") and `t_round14_v2r_b2_*` fails ("the procedure's reduction is not round 14's"); the search's mutations (the limit's line with the band's budgeted 9.16 K for the measured baseline, or every junction at round 13's fixed split) each accept specimens over 150 C. The procedures' own quote verifier on TP-E11-29 in this tree: every quote of this record matches (2 table, 12 text); the two failures it reports are L4-E9's cells (R-159's Acceptance, 5d's What to buy), older in this branch's tree than on set 29's line, as round 13 recorded. Set 29's fixture-test anchor "(Zself + 2 Zmut) at most 40.78 K/W steady" still occurs once in the procedure. The page's dependency table (section 11) re-cites its ten record lines, moved by this round's In short bullet.

**ROUND 13 (DELTA-02, branch `fnd/l4e11r11`, 4 October 2026): DONE on the desk. What is done: the owner's supplier-delta review's DELTA-02 (P1) answered in the record AND in the procedure: the method selected (B), E11-29 restated on it, `v2/docs/test-procedures/TP-E11-29.md` rewritten on it by the coordinator's instruction (the owner: "complete the selected measurement method, reconcile the procedure and calculations, and run its focused check"); section 20c restated on Murata's printed points. What is not done: nothing bought, built or measured; the method has had NO independent check (the focused check is the coordinator's to schedule); TP-E11-29 stays NOT EXECUTABLE; the first prototype's gate links are not drafted; the guard's reading on DD-7 is owed. Next action: the focused check of section 23 with TP-E11-29, then the limits agreed (R-159 restated by L4-E9 from E11-29's row) and a supplier's agreement to the fixture.** Case row C-PROT rev 1. Tests `t_round13_*`; at this round `test_l4e11` and `test_public_hygiene`: 77 passed, 0 failed, 0 skipped. The round is the author's own work and has had no independent check: UNVERIFIED.

DELTA-02 answered (the review as received: `_runs/claude/inputs-20261004e/REVIEW-SUPPLIER-DELTA-AA76C894-AS-RECEIVED.md`, sha256 `73efaadf`; filing it is the integrator's):

| Item | What changed | File |
|---|---|---|
| **The defect, confirmed** | Q39, Q40 and Q42 are drawn by one statement of the charger draft: every gate on CH_BATDRV, every drain on CH_BATQ, every source on VBAT (read by `ast`; the same in the regenerated netlist, read by `check_dd7_netlist.py`'s reader). Nexperia BUK6Y10-30P (17 April 2020) Table 2 p.2: pins 1 to 3 source, 4 gate, the mounting base the drain; the diode rows IS 80 A (p.3), VSD 0.7 / 1.2 V at 80 A (p.6). So the three body diodes are in parallel, and "each FET heated through its body diode alone, each junction by its own VSD" was never defined. Rounds 11 and 12 changed the limit and kept that method | `l4e11_power.py` (`charger_fets`, `per_device`, `fix23_round`), out and page 23a |
| **Three methods compared** | (A) a coupon with a source island and link for each device, body-diode heating: per-device, but the VBAT source pour is cut, Zmut reads LOW and heat arriving through the VBAT copper reads LOW; budget 2.89 % plus a transfer term no coupon gives. **(B) the pours as board A's and the three gates brought out apart: one channel heated at a time, selected by its gate, the current entering at the source (the other two off, their body diodes reverse-biased); each junction read by that FET's threshold with its gate on its drain.** (C) the three diodes together: the total power and one voltage, a 20 K bracket on the hottest junction, no device's power known: it cannot decide the acceptance | out and page 23b, 23c |
| **SELECTED (SESSION): (B)** | the only one that leaves the copper as board A's, gives each device's power and junction with no assumption about sharing, and imposes the worst split itself (time division). Reversed by: the two threshold calibrations differing by more than 0.5 K, reciprocity failing beyond the budget, or no supplier agreeing: then (A) on the 40.78 K/W bar alone. The first prototype is not a specimen for (B) until each gate branch has a removable link (NOT DRAFTED) | out and page 23d |
| **E11-29 restated** | each FET alone at 1.345 W and 1.513 W (the 3 x 3 matrix of Zself and Zmut, reciprocity checked), the three evenly and the worst split (1.513 / 0.756 / 0.756 W, each FET in turn) by time division in slots of at most 244 us, the band and R17 on. Budget 3.22 % (K-factor 2 %, power 1 %, air 1.82 %, repeatability 0.91 %, leakage 0.55 %, ripple 0.95 %): **a reading of 39.51 K/W or under passes the 40.78 K/W bar** (44.45 against 45.88 K/W for m at or over 1/4; the worst split's hottest junction 71.45 K or under over the air against 73.75 K). The PTC's site read by a thermocouple in every case, its gradient RECORDED | E11-29's row (section 8, rendered by `e11_29_method`), block E11-29 (17d), out and page 23e |
| **TP-E11-29 rewritten on (B)** | the fixture with its current paths in calibration, heating and sensing, the equipment, 14 steps, six validity checks (V1 to V6), each power and temperature with its uncertainty, the reduction to Zself and Zmut and the bar, RT1's land, the transfer rule. Status **NOT EXECUTABLE**, naming what must happen first (the independent check, the limits agreed, a supplier's agreement). Every quote of THIS record matches it (the procedures' own verifier, in `test_l4e11`) | `v2/docs/test-procedures/TP-E11-29.md`; out and page 23f |
| **Section 20c on the printed points** (record l9stk's round 4) | the PRF15BB103 prints 10 kOhm +-50 % at 25 C, 100 kOhm over 110 C and 4.7 MOhm at 130 +-3 C. 20c's "bound point (10.6 V, RT1 47 kOhm)" and the 2.952 / 2.894 V read on it, and 20f's "at least 2.894 V ... 2.054 V to spare", bound nothing and are restated in place. At 100 kOhm and 10.6 V the first inverter is not defined (1.714 V). A tripped PTC is read held with the loop powered, so a guard trip sets DD-7's inhibit; with record l9stk's selected temperature switch (not drafted) that happens at the trip itself: an OWED reading | out and page 20c, 20f, 23g; `inputs/l9stk-section15.5-guard-43da41ca.md` (copied from `fnd/l9stk2` at `43da41ca`) |

The method's assumptions, plainly:

| Figure | What it is |
|---|---|
| the pinning, the body diode's direction, IS 80 A, VSD 0.7 / 1.2 V, ID 57 A at a 100 C mounting base, IDSS 1 uA at 25 C and 10 uA at 125 C, the threshold 1.5 / 2 / 3 V at 250 uA and 25 C | the maker's printed limits (Nexperia BUK6Y10-30P, 17 April 2020: Table 2 p.2, Table 5 p.3, Table 7 p.6) |
| **the threshold's temperature coefficient** | **NOT PRINTED.** Nexperia prints the 25 C row and a curve against junction temperature (Fig. 11, p.8), a typical figure. The method uses no printed coefficient: the K-factor is calibrated on each of the coupon's three FETs in an oven, twice |
| the device's 0.2589 K/W at 244 us (the ripple's bound) | read by this record from the maker's Fig. 4 (section 16b), scaled to the printed 1.4 K/W: a reading of a curve, INFERRED |
| the K-factor within 2 %, the power within 1 %, the air within 1 K | the record's own terms (block E11-29, round 9), limits the supplier's instruments must meet |
| the sense current 1 mA, the slot 244 us, the repeatability 0.5 K, the leakage term 0.3 K | ASSUMED (SESSION proposals), the supplier's to confirm or replace |
| the gate traces carry no heat of consequence; superposition and reciprocity (linear conduction) | INFERRED |
| method (C)'s bracket (ideality 1, 2 mV/K) | ASSUMED, used only to reject (C) |
| **What the method cannot bound** | the threshold's drift under repeated gate drive beyond what the two calibrations show; the off devices' leakage over 125 C (unprinted; the procedure's check V3 reads it); the coupon's difference from the built board (the comparison rule's matter); whether 40.78 K/W can be met at all (no printed or measured figure shows it) |

For the integrator and other authors (nothing of theirs is edited here):
- **L4-E9:** R-159's Acceptance still carries round 9's 45.88 K/W and no method; 5d's Specimen cell still offers the first prototype. Both are restated from E11-29's row and block. TP-E11-29 quotes them as they stand on set 29's line.
- **The procedures folder:** `tp_check` on a scratch copy of the candidate's docs (`dfa1eef2`) with this round laid over reads TP-E11-29.md with no failure. One failure remains there that this record caused in rounds 11 and 12 and may not repair: `TP-E11-37.md`'s quote of row E11-37's Acceptance (the row gained Q-TI-17 (e) and (f) and the pair as the correction scope). `tp_check.out` pins each procedure's sha256 and is regenerated at integration, after that re-quote. Set 29's `test_test_procedures.py` builds a broken copy of TP-E11-29.md from the anchor "45.88 K/W steady by the body diode" (its line 155), which the rewritten procedure no longer carries: the anchor "(Zself + 2 Zmut) at most 40.78 K/W steady" occurs once in it, and changing it to 41.78 makes the checker fail the row's quote (tried on the scratch copy); its other anchors (the mark, `register: R-159`, `## 3. Safety`, `TBD (owed by R-159)`, the R-159 quote's attributes) are all still there. In THIS branch's tree the folder and its test are main's (older than set 29), so `tp_check` also reports two of TP-E11-29's quotes of L4-E9's cells (R-159's Acceptance, 5d's What to buy) and three older failures, and `test_test_procedures` reads 10 passed, 4 failed here. `tp_check` already failed in this tree before this round (five failures: this record's rounds 9 to 12 against main's procedures), which is what three of those tests read; the fourth, the fixture test, now misses main's own anchor "33.12 K/W steady and at 60 s" in the rewritten procedure (set 29's version of the test uses the anchor named above).
- **Board A's generator and Layer 9:** a removable link in each battery FET's gate branch would make the first prototype a specimen; not drafted.
- **Record l8p with this record:** the guard's draft (record l9stk's selected switch) and its reading on DD-7 (23g).
- **Record l8p's round 6** changed its PTC draft's bytes; `test_l4e11` pins that draft and is re-pinned at integration.

**ROUND 12 (branch `fnd/l4e11r11`, 4 October 2026, after the independent check V2): DONE on the desk. What is done: V2-B1 answered by correction (b), R256 back to 4.7 kOhm, with V2's arithmetic reproduced and its three corrections compared against both needs (record and output section 22); V2-m1 to m5 and m9 carried. What is not done: nothing bought, built or measured; need 1 (the bleed at the hot bound inside the hold) stays CONDITIONAL and OPEN on record l8p's E-14c and this record's E11-45 (f2), because the breaker FETs' hot leakage is unprinted; E11-37, E11-29 and E11-36 as round 11 left them. Next action: the targeted recheck of V2-B1's correction (sections 22a to 22g, 20e, 20g and the draft's R256), then E-14c and E11-45 (f2) on the specimen.** Case row C-PROT rev 1. Tests `t_round12_*` in `v2/ecad/tools/tests/test_l4e11.py`; at this round `test_l4e11` and `test_public_hygiene`: 73 passed, 0 failed, 0 skipped; `test_l8p`: 9 passed, 1 failed (`t_the_committed_output_is_what_the_script_prints`: `l8p_drafts.out` pins older L4-E11 drafts, the check V2's V2-B2, record l8p's or the integrator's). The round is the author's own answer to V2's first negative check of the 6.8 kOhm value: UNVERIFIED until the targeted recheck.

V2's findings answered (the check as received: `_runs/claude/inputs-20261004e/CHECK-V2-AS-RECEIVED.md`, sha256 `bddebb4c`; filing it under a `checks/` folder is the integrator's):

| Finding | What changed | File |
|---|---|---|
| **V2-B1** (blocking): the bleed's 0.112 s margin beside the 0.597 mA limit | V2's arithmetic reproduced (the script refuses a figure that differs by more than 1.2 %, and refuses a bleed that counts no source). The sources at their hot bound on C-PROT rev 1: 434.8 uA (the LM5069's 1 MOhm 16.8 uA; the battery FETs 30 uA on Nexperia's printed 125 C row; the breaker pair 388.0 uA on record l8p's ASSUMED doubling, L8P-F06). V2's three corrections on one basis: (a) text only FAILS need 1 (2.189 s against the hold's 1.341 s; coupled limit 87.4 uA); (c) 6.8 kOhm with C241 2.2 uF holds it by 0.396 s (limit 498 uA) but moves the hold to 12.8 s at most and the arm to 0.91; **(b) SELECTED (SESSION): R256 back to 4.7 kOhm**, the bleed 1.218 s at the hot bound, 0.123 s inside the hold, coupled limit 520.7 uA (the pair may leak 473.9 uA: 103.9 C on the assumed doubling), static limit 0.846 mA; (c) at 3.3 uF would allow the pair 36.9 uA more (about 1.1 K on the assumed rate) with a hold of up to 19 s, which does not remove the dependence. Need 2: U47's RESET 3.85 mA at the set, 3.72 mA with the breaker restarted, 4.32 mA with CELL+ at SYSOVP 19.5 V, against TI's recommended 5 mA (SNVSBJ1E 7.3 p.6); 6.45 mA, under the absolute 10 mA (7.1 p.6), only with CELL+ over 22.51 V: a surge at the instant of a set, or a shorted battery FET with VBAT held over SYSOVP (two faults). No correction holds need 1 on printed figures (TI SLPS632 p.3 prints the CSD18510Q5B's IDSS at 25 C only), so the finding stays **OPEN** on E-14c and E11-45 (f2). V1's and V2's arithmetic side by side in 22f | `l4e11_power.py` (section 22, `bleed_time`, `dd7_variant`, `fix22_round`), `l4e11_power.out` (20e, 20g, 21f, 22), the page (20e, 20g, 21f, 22), `apply_gen_sch_a_dd7.py` (R256 4.7k), `check_dd7_netlist.py` (R256 4.7k; the BODY group: the battery FETs' source on VBAT, drain on CH_BATQ), E11-45 (f2) and (h) in section 8, `inputs/l8p-section12j-f06-69156072.md` (record l8p's F06 as written at `fnd/l8p2` `69156072`), `test_l4e11.py` (`t_round12_v2b1_*`; the compose test's mutations R256 at 6.8k and a reversed battery FET) |
| **V2-m1**: Vishay's Ciss called "printed maxima" while the typical column was taken | the maxima are the figures judged (SQJ403EP 4.5 nF, SQJ407EP 10.7 nF; Vishay 67109 Rev. A and 62806 Rev. B), the typical figures printed beside them; the verdict unchanged | `l4e11_power.py` (`fix21_round`, 21b), out 21b, page 21b |
| **V2-m2**: the battery FETs' hot leakage called "not printed" | Nexperia's row quoted: IDSS at most 10 uA at Tj 125 C, VDS -30 V (BUK6Y10-30P, 17 April 2020, Table 7 p.6); nothing over 125 C | out and page 20e and 22b |
| **V2-m3**: the dd7 draft's comment "at most 4.4 mA at the clamp" | restated from 22c: 3.85 mA at the set, 4.32 mA with CELL+ at SYSOVP, 6.45 mA only at the clamp; a test reads the comment against the script | `apply_gen_sch_a_dd7.py` |
| **V2-m4**: two of V1's minors carried by no record | named in 22h, each with an owner and a next action: the TPS37's hysteresis accuracy read as percentage points (V1's three figures reproduced by the script; owner this record; Q-TI-19 drafted, NOT SENT, and E11-45 (e)); the CONOPS wording of the named residual (a sentence drafted; owner the CONOPS owner with record l9stk; next L4-E9's register row). Filing V1's check is the integrator's | out and page 22h, `clarification/TI-QUESTIONS.md` (Q-TI-19) |
| **V2-m5** (this record's half): the guard's trip side adds the even split's rise | E11-29's coupon reads the PTC's site against each junction with one FET heated alone at the worst split's 1.513 W | E11-29's row (section 8) and block (17d) |
| **V2-m9** (this record's half): the tests compose board A in main's order | the candidate's list (L4-E9 rows 24 to 33) names record l8r2's packrtn, slotlm and fb01; those three drafts are NOT in this branch's tree (`fnd/l8r3` at `89924e40`), so the existing tests keep the order this tree can show (main's, with l8r2's d8v3 and vbus20ov), the difference named in `_ORDER9`'s comment and in 22h. New: `compose_in_list_order.py TREE WORK` composes the list's order where its drafts are. Run on a scratch copy of the candidate's files (`git archive dfa1eef2` of the tools and the ten records, this round's drafts laid over): 16 drafts each exit 0, the generator to its end (778 parts, intent written), DRAWN, three mutations FAIL. `test_l4e11` runs it: here it reports the missing drafts (exit 1); on the candidate's line it requires exit 0 | `compose_in_list_order.py`, `test_l4e11.py` (`_ORDER9`'s comment; `t_round12_the_minors_*`), out and page 22h |

**Round 11 (T2, 4 October 2026), as the independent check V2 read it** (item A CONFIRMED AS CONDITIONAL; item B's R256 claim NOT CONFIRMED and answered by round 12 above): Case row C-PROT rev 1 (`_runs/cases/CASES-2026-10-04.md`). Record section 21, output section 21, tests `t_round11_*` in `v2/ecad/tools/tests/test_l4e11.py`.

Round 11's changed claims, for the next independent check (V2):

| Claim | Where | Source (document, revision, page) | Label |
|---|---|---|---|
| E-1 fails at its own case with the even split: one FET at R / 2 takes 9/8 of the even loss, 157.7 C held at 23.93 A at 45.88 K/W | page 21a, out 21a | record l9stk `L9-STACKUPS.md` 15.5 at `0d72880b` (45.88 K/W, 23.93 A, 76.25 C, the band 9.16 K, R17 2.86 K); Nexperia BUK6Y10-30P (17 April 2020) Table 7 p.6 prints RDS(on) maxima and no minimum | INFERRED (closed form, scanned in the test) |
| round 10's 20i "Zmut under Zself / 7" holds for the split R / 2 only; over every split the region is Zmut under Zself / 4 | page 20i and 21a, out 20i and 21a | the script's `worst_share` and `split_share` | INFERRED |
| E-1's installed acceptance becomes (Zself + 2 Zmut) at most **40.78 K/W** for any split (45.88 x 8 (1 - m)(1 + 2 m) / 9 with Zself and Zmut read apart, the largest of each) | E11-29 (section 8), block E11-29 (17d), page 21b/21d, the charger draft's layout comment | as above; no sheet prints an installed RthJA for the BUK6Y10-30P (Table 6 p.5: Rth(j-mb) 1.4 K/W only) | SESSION selection; CONDITIONAL on E11-29 (coupon) and E11-36 (the 21.136 mOhm allowance) |
| the allowance is taken at the charger's printed least drive, VBATDRV_ON 8.5 V; at 10 V it would read 15 mOhm | page and out 21a | TI SLUSE65A p.17 (VBATDRV_ON); the BUK6Y10-30P's printed maxima, section 15c's two chords | MAKER, INFERRED |
| three approaches: (i)(a) SELECTED; (i)(b) PXP9R1-30QL 32.85 K/W, rejected; (ii) the pair 20.39 K/W, under 5 nF only on a typical figure (4.72 nF at -15 V, about 5.74 near 0 V), the correction scope if E11-37 refuses three; (iii) a buffer on BATDRV, no printed basis | page 21b to 21d, out 21b to 21d | Nexperia PXP9R1-30QL (product data sheet, 5 January 2021; held, sha256 88a7b67b); AOS AONS21357 Rev 2.1; Vishay SQJ403EP Rev A, SQJ407EP Rev B; BUK6Y10-30P Table 7 p.6 and Fig. 12; TI SLUSE65A 9.2.2 p.92 (5 nF), pin table p.5 and 8.4.1.1 p.38 (BATDRV) | MAKER (Ciss typical except the two Vishay maxima), INFERRED, SESSION |
| E11-37 stays OPEN; Q-TI-17 (e) the 5 nF's VDS and the pair's typical figure, (f) the gate load TI accepts and any buffer | `clarification/TI-QUESTIONS.md`, E11-37's row | TI SLUSE65A p.92 | drafted, NOT SENT |
| V1's minors: R84 specified pulse-rated. R256's move to 6.8k and the trade round 11 printed for it (sources under 0.597 mA, the bleed 1.228 s, 0.112 s of margin) are WITHDRAWN and superseded by round 12 (V2-B1) | page 20 and 21f, out 20 and 21f, `apply_gen_sch_a_dd7.py`, `check_dd7_netlist.py` | TI SNVSBJ1E (TPS37, recommended RESET current and VOL rows); Yageo RC1206 (the 5 s overload comparison withdrawn) | SESSION; R84's part CONDITIONAL (Layer 6) |

Closure credit for round 11: (a) board A composes in L4-E9's order and runs to its end (`test_l4e11`); (b) E-1's correction changes no net (the bar is an acceptance), V1's minors are read in the regenerated netlist by `check_dd7_netlist.py` (DRAWN; eight mutations FAIL since round 12: R256 at 6.8k, R84 without its rating and a reversed battery FET among them); (c) on C-PROT rev 1, the hottest junction at most 150 C held at 23.93 A from 76.25 C over a scan of every split under the allowance at m 0 to 0.4, and the even split's bar, a bar 1 % looser, the split read as even and the allowance read at a 10 V drive each FAIL (`t_round11_e1_holds_on_c_prot_over_every_split_and_its_mutations_fail`). Tests at round 11: `test_l4e11` 67 passed, 0 failed, 0 skipped; `test_l8p` and `test_public_hygiene` 13 passed, 1 failed (`test_l8p.t_the_committed_output_is_what_the_script_prints`: `l8p_drafts.out` pins older L4-E11 drafts, V1's C4, record l8p's or the integrator's). Round 11's correction is the author's own reading: UNVERIFIED until V2.
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
