meshsat/meshsat-fieldkit/compact/v2/renders/renders_button_detail.png

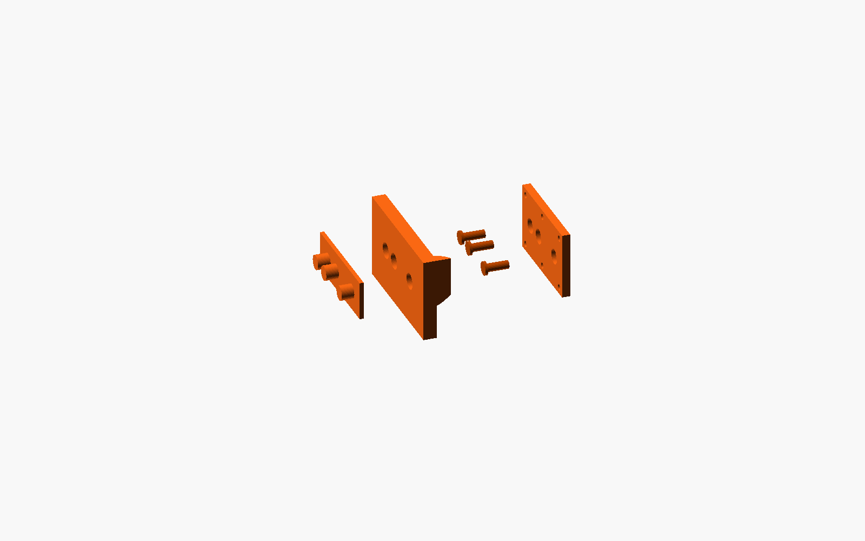
compact/v2/renders/renders_button_detail.png
