meshsat/meshsat-fieldkit/compact/v2/renders/renders_exploded_front.png

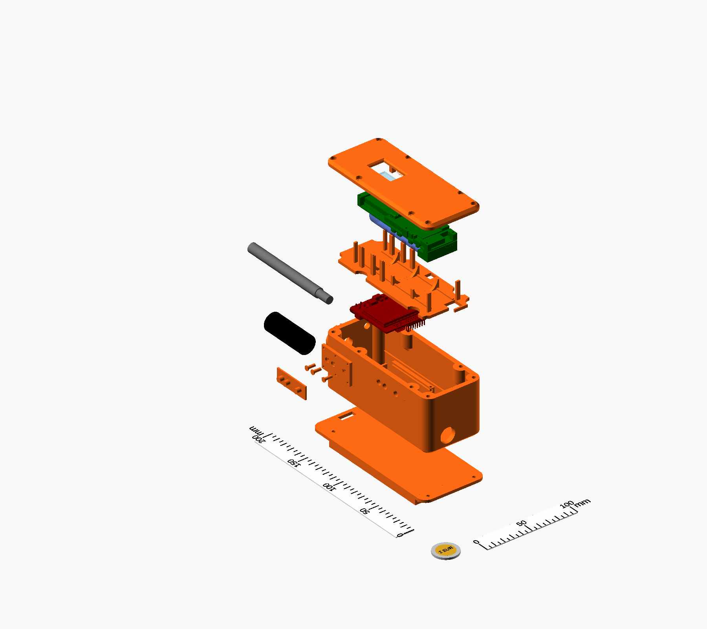
compact/v2/renders/renders_exploded_front.png
