meshsat/meshsat-fieldkit/v2/cad/render/ui.png

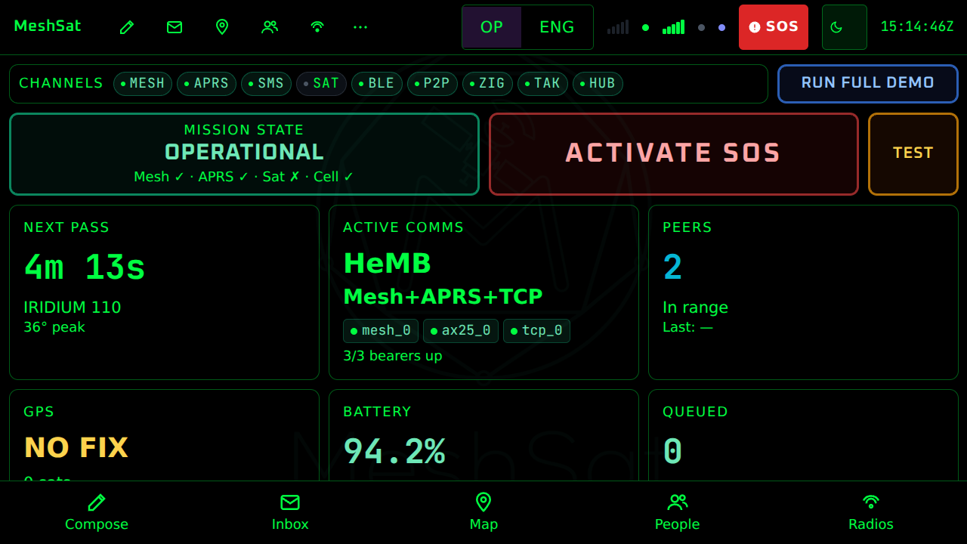
v2/cad/render/ui.png
