meshsat/meshsat-fieldkit/v2/ecad/easyeda-pro/pcb-a-power-A22/pcb-a-power-A22-pcb-view.jpg

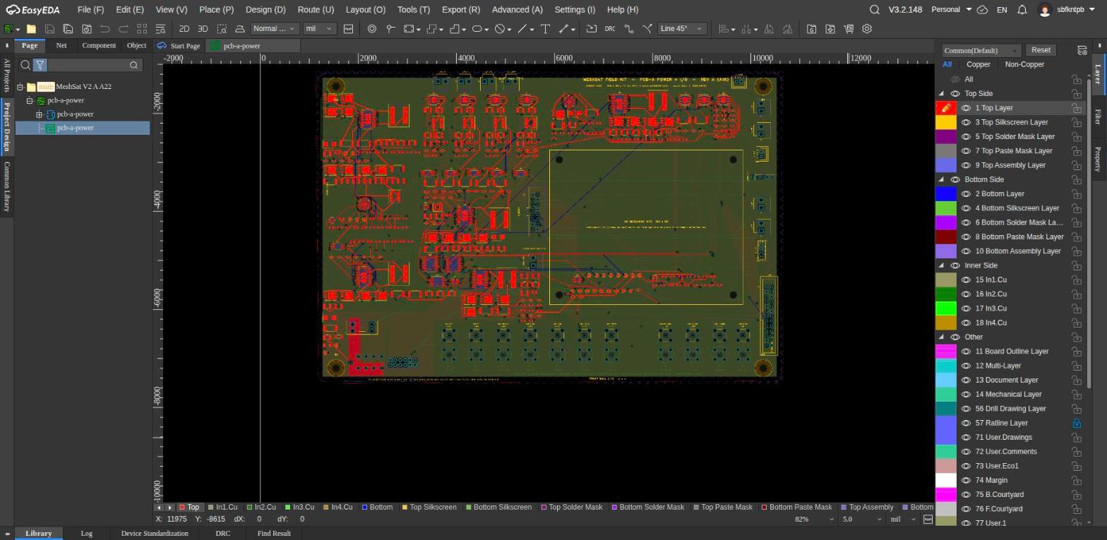
v2/ecad/easyeda-pro/pcb-a-power-A22/pcb-a-power-A22-pcb-view.jpg
