meshsat/meshsat-fieldkit/v2/ecad/easyeda-pro/pcb-b-compute-B16/pcb-b-compute-B16-pcb-view.jpg

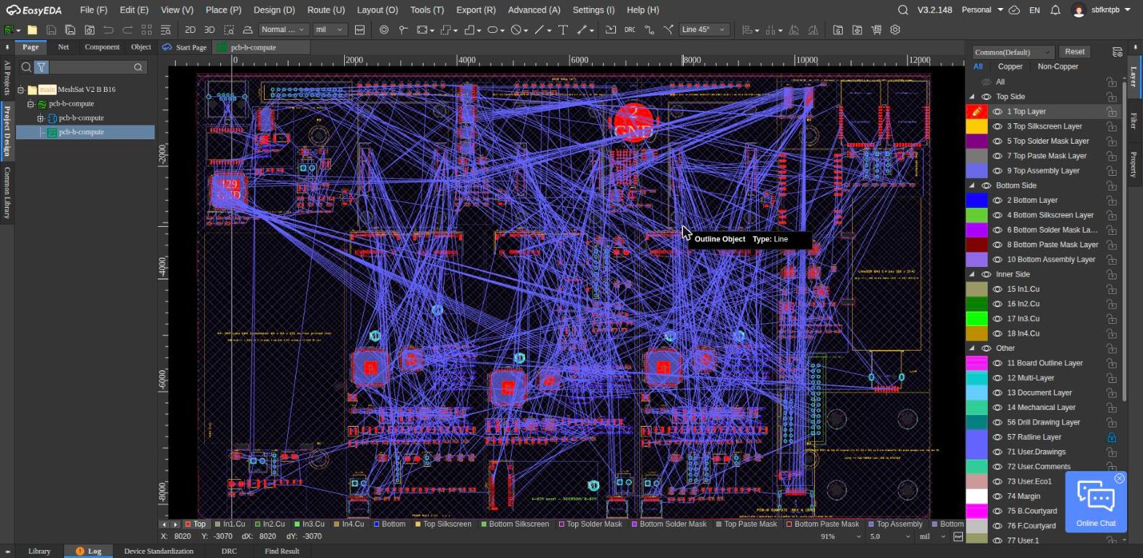
v2/ecad/easyeda-pro/pcb-b-compute-B16/pcb-b-compute-B16-pcb-view.jpg
