meshsat/meshsat-fieldkit/v2/ecad/easyeda-pro/pcb-c-display-C7/pcb-c-display-C7-3d-view.jpg

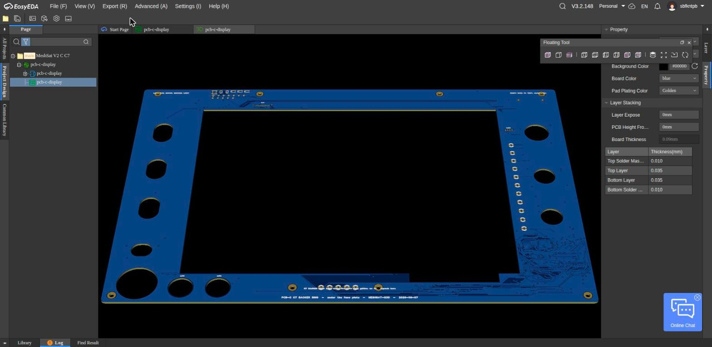
v2/ecad/easyeda-pro/pcb-c-display-C7/pcb-c-display-C7-3d-view.jpg
