meshsat/meshsat-fieldkit/v2/ecad/easyeda-pro/pcb-d-aprs-D8/pcb-d-aprs-D8-pcb-view.jpg

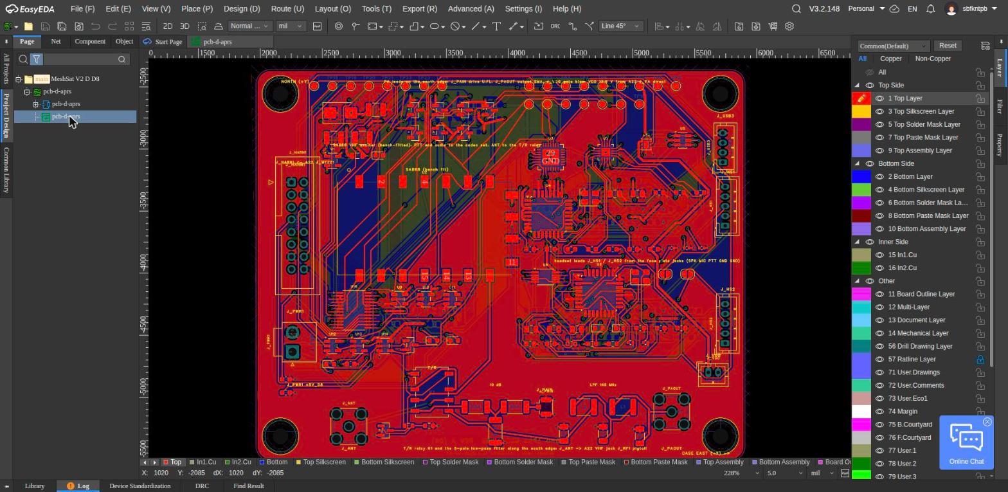
v2/ecad/easyeda-pro/pcb-d-aprs-D8/pcb-d-aprs-D8-pcb-view.jpg
