meshsat/meshsat-fieldkit/v2/ecad/easyeda-pro/pcb-e1-dock-E6/pcb-e1-dock-E6-pcb-view.jpg

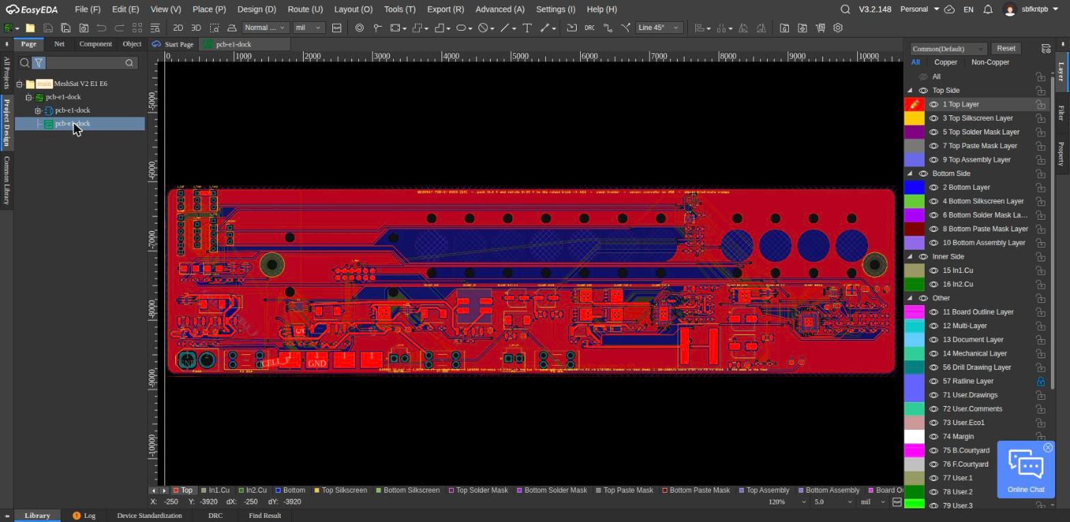
v2/ecad/easyeda-pro/pcb-e1-dock-E6/pcb-e1-dock-E6-pcb-view.jpg
