meshsat/meshsat-fieldkit/v2/ecad/easyeda-pro/pcb-e5-block-E5/pcb-e5-block-E5-pcb-view.jpg

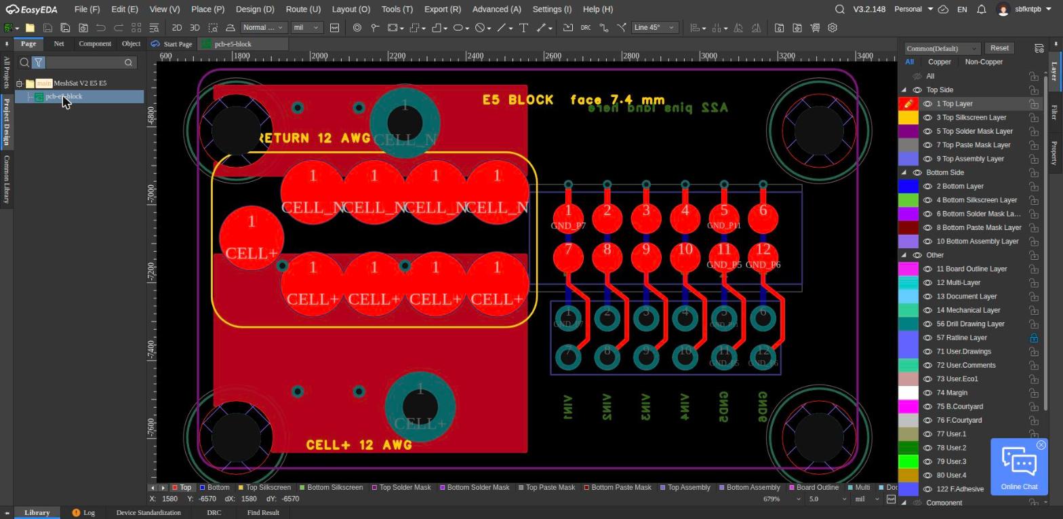
v2/ecad/easyeda-pro/pcb-e5-block-E5/pcb-e5-block-E5-pcb-view.jpg
