meshsat/meshsat-fieldkit/v2/ecad/easyeda-pro/pcb-p-pack-P2/pcb-p-pack-P2-pcb-view.jpg

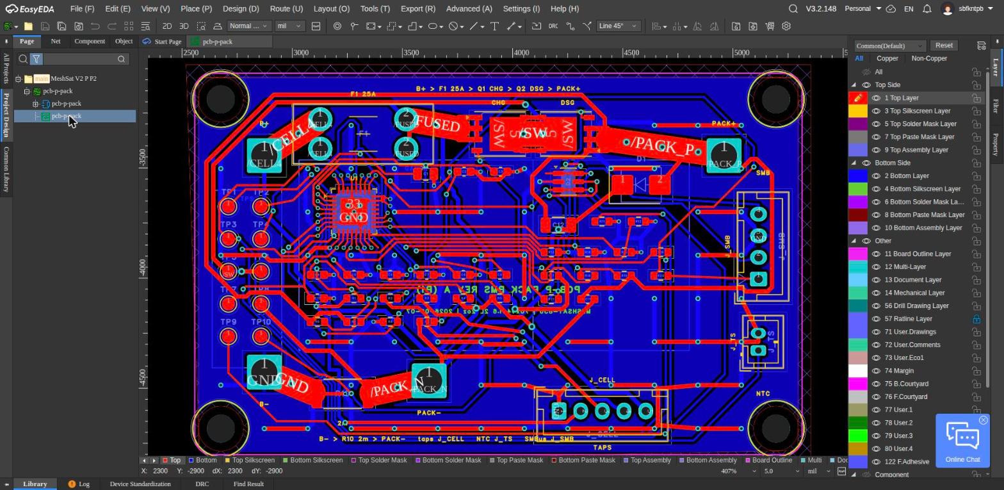
v2/ecad/easyeda-pro/pcb-p-pack-P2/pcb-p-pack-P2-pcb-view.jpg
