meshsat/meshsat-fieldkit/v2/images/boards-3d/pcb-a-power-A24-bottom.png

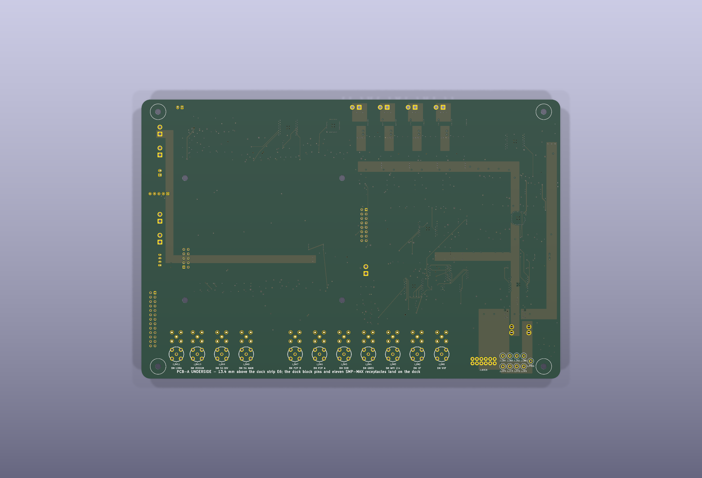
v2/images/boards-3d/pcb-a-power-A24-bottom.png
