meshsat/meshsat-fieldkit/v2/images/boards-3d/pcb-b-compute-B19-bottom.png

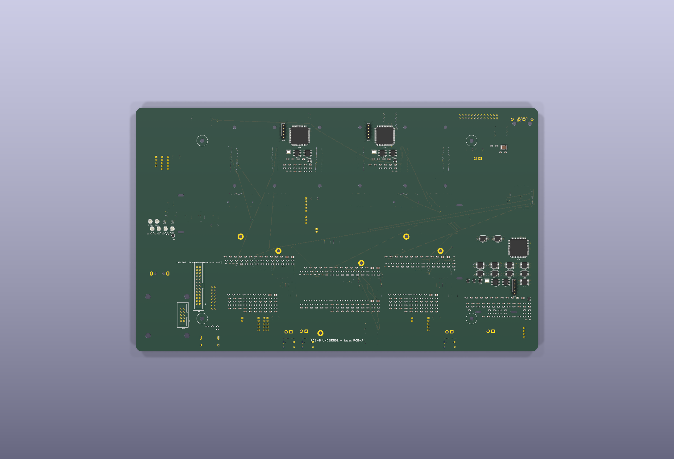
v2/images/boards-3d/pcb-b-compute-B19-bottom.png
