meshsat/meshsat-fieldkit/v2/images/boards-3d/pcb-c-display-C10-top.png

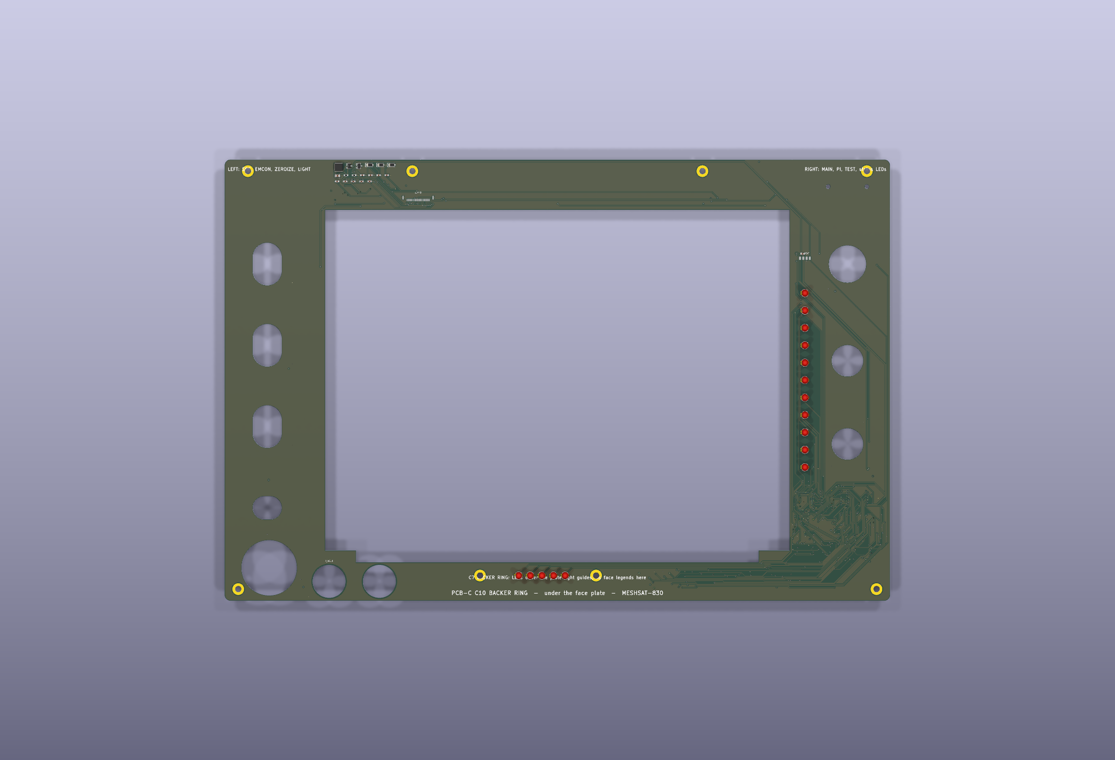
v2/images/boards-3d/pcb-c-display-C10-top.png
