meshsat/meshsat-fieldkit/v2/images/boards-3d/pcb-d-aprs-D10-bottom.png

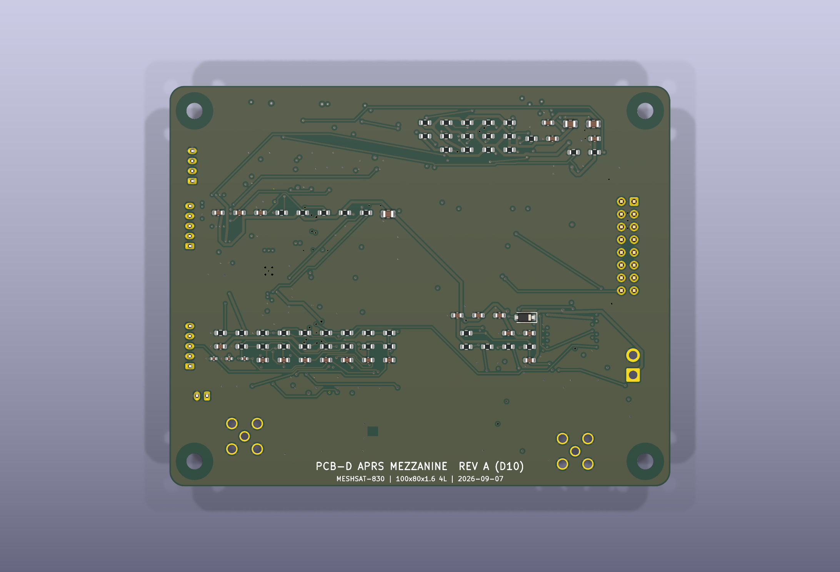
v2/images/boards-3d/pcb-d-aprs-D10-bottom.png
