meshsat/meshsat-fieldkit/v2/images/boards-3d/pcb-e1-dock-E7-bottom.png

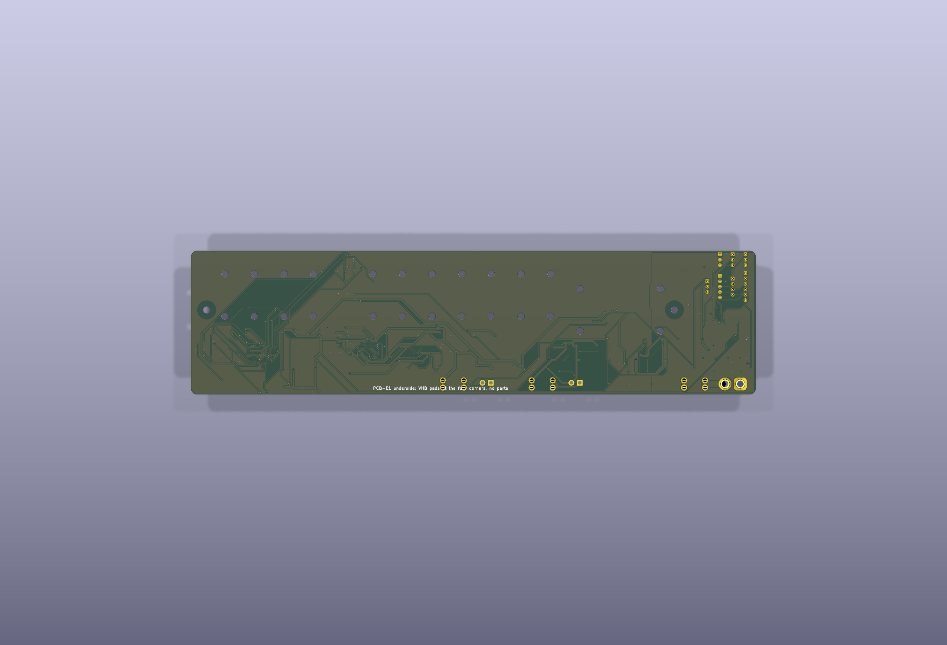
v2/images/boards-3d/pcb-e1-dock-E7-bottom.png
