meshsat/meshsat-fieldkit/v2/images/boards-3d/pcb-e5-block-E5-top.png

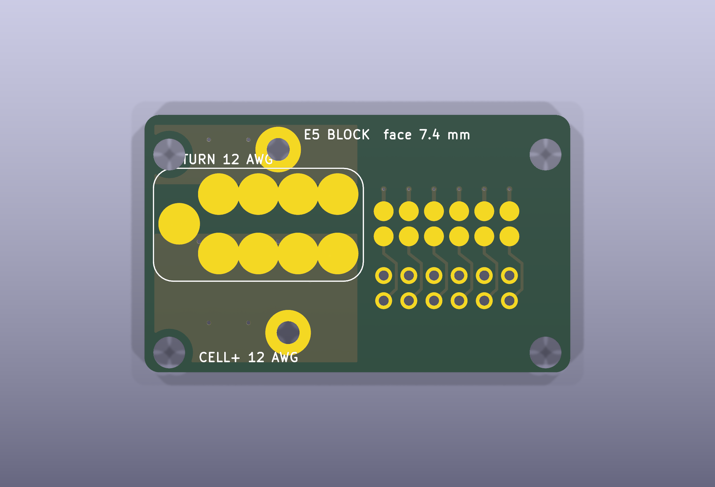
v2/images/boards-3d/pcb-e5-block-E5-top.png
