meshsat/meshsat-fieldkit/v2/images/boards-3d/pcb-p-pack-P3-bottom.png

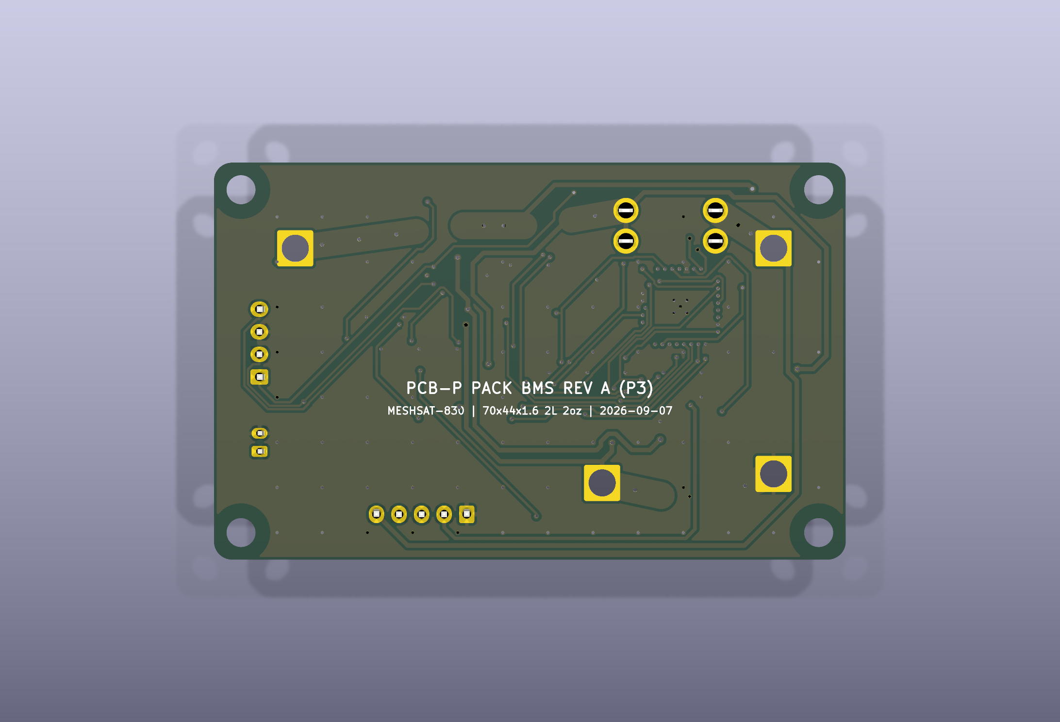
v2/images/boards-3d/pcb-p-pack-P3-bottom.png
