meshsat/meshsat-fieldkit/v2/images/concept-1450/set-ten/09-face-detail-right.png

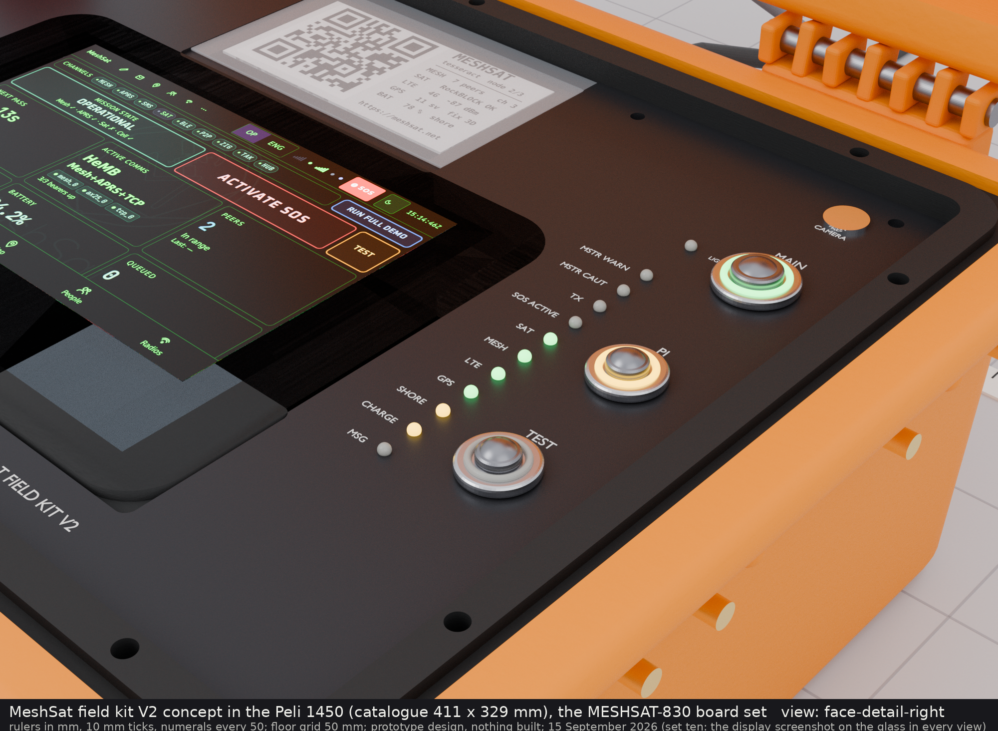
v2/images/concept-1450/set-ten/09-face-detail-right.png
