meshsat/meshsat-fieldkit/v2/images/concept/meshsat-v2-concept-closed.png

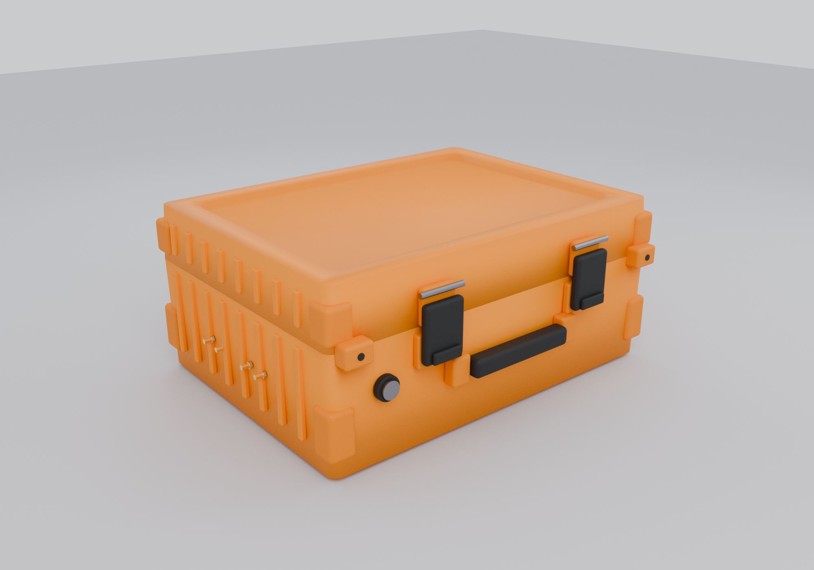
v2/images/concept/meshsat-v2-concept-closed.png
