meshsat/meshsat-fieldkit/v2/images/concept/meshsat-v2-concept-cutaway.png

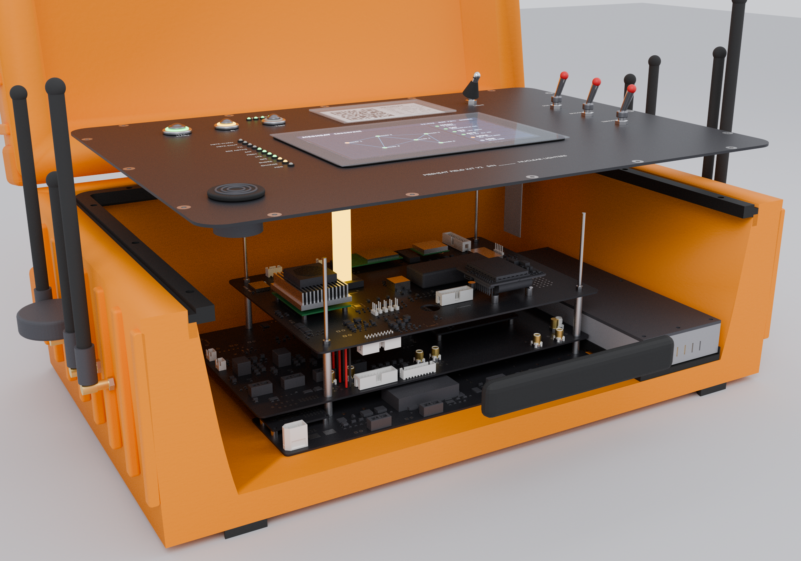
v2/images/concept/meshsat-v2-concept-cutaway.png
