meshsat/meshsat-fieldkit/v2/images/concept/meshsat-v2-concept-detail.png

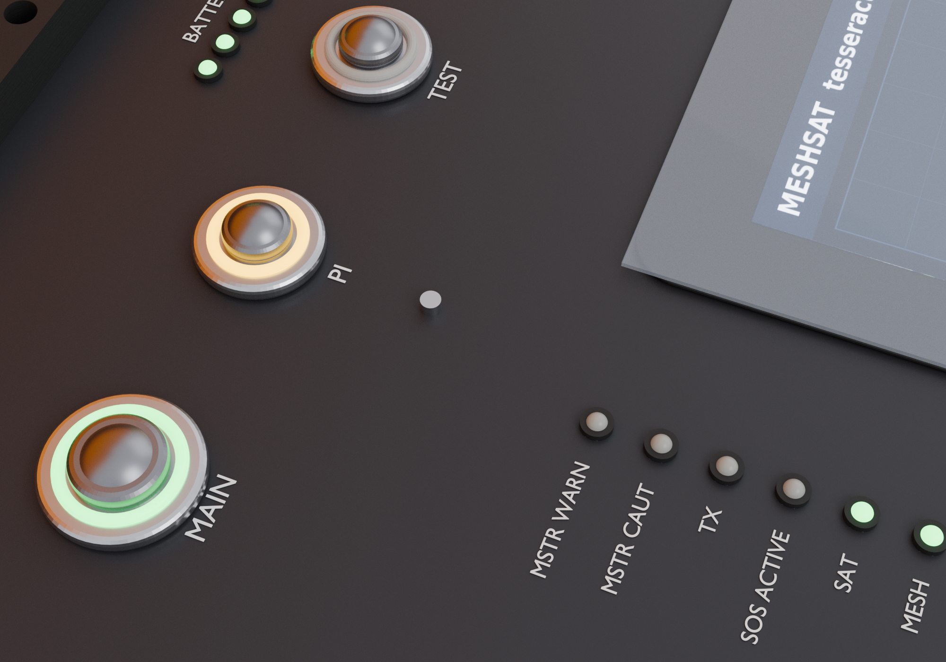
v2/images/concept/meshsat-v2-concept-detail.png
