meshsat/meshsat-fieldkit/v2/images/concept/meshsat-v2-concept-hero.png

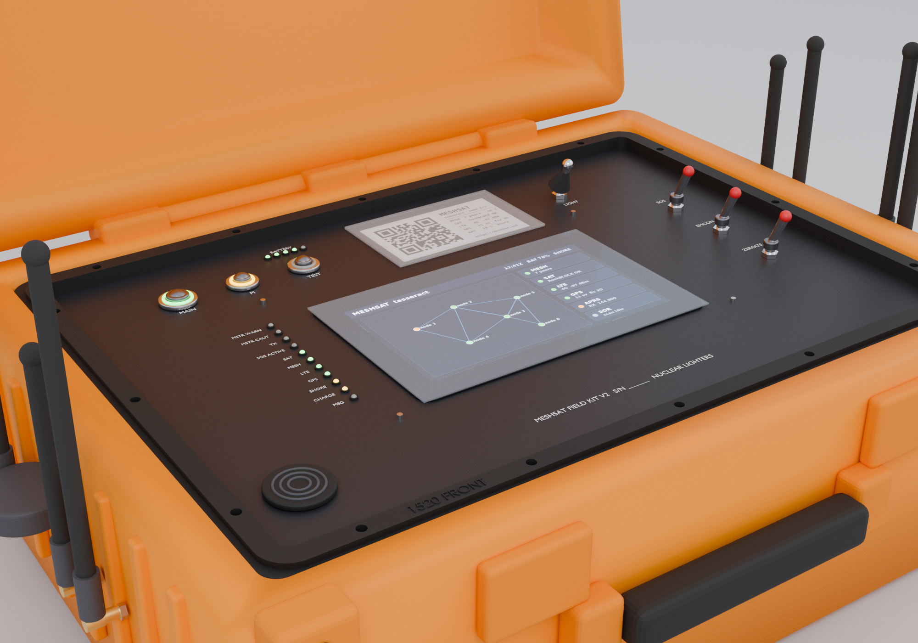
v2/images/concept/meshsat-v2-concept-hero.png
