meshsat/meshsat-fieldkit/v2/images/concept/meshsat-v2-concept-overview.png

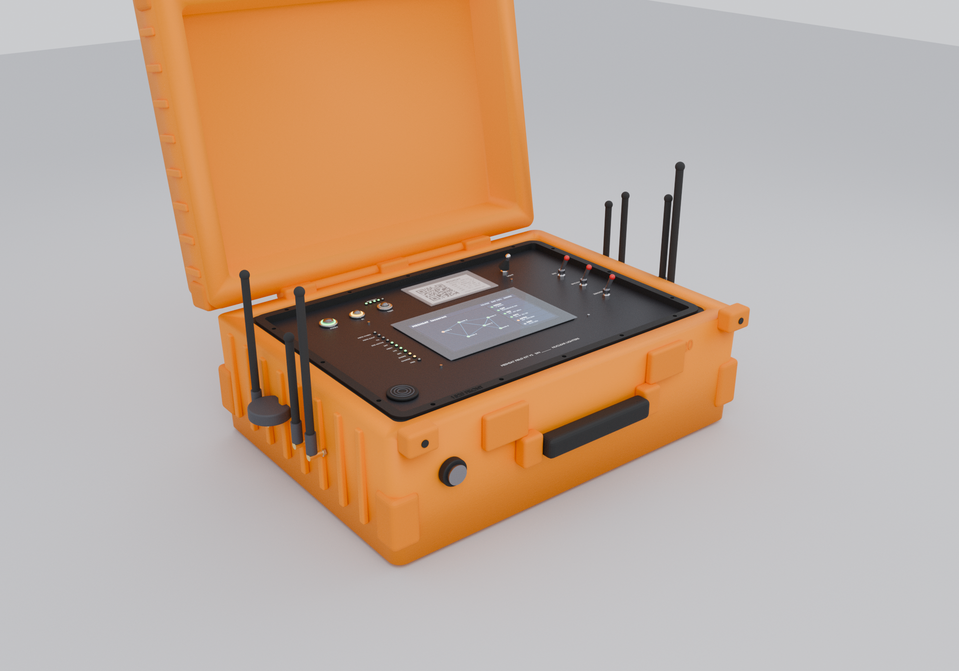
v2/images/concept/meshsat-v2-concept-overview.png
