meshsat/meshsat-fieldkit/v2/images/concept/meshsat-v2-concept-top.png

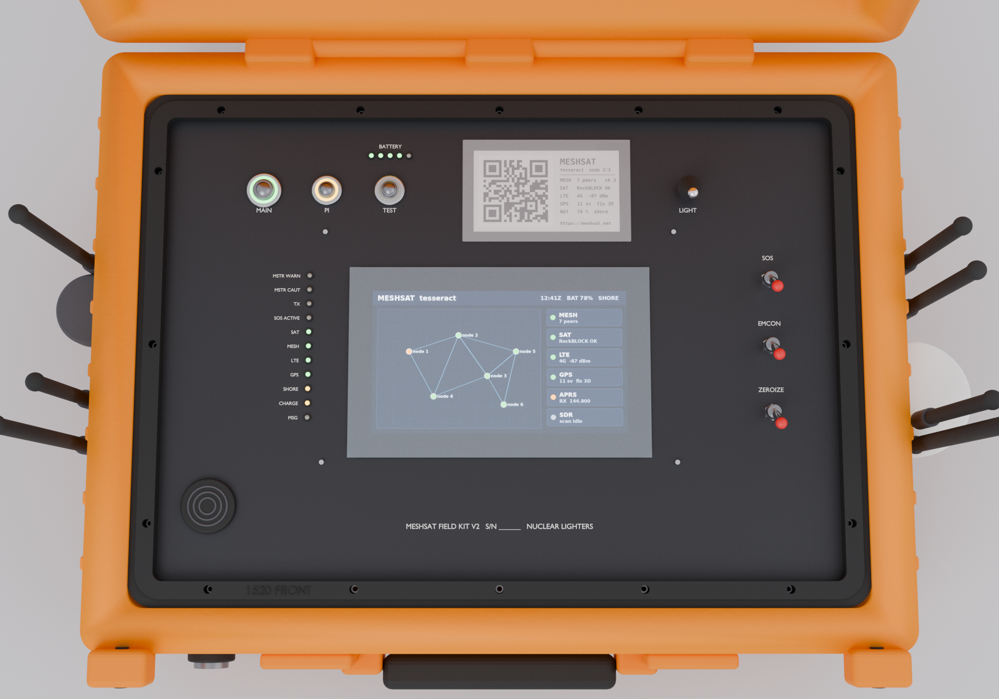
v2/images/concept/meshsat-v2-concept-top.png
