meshsat/meshsat-fieldkit/v2/images/face-section.png

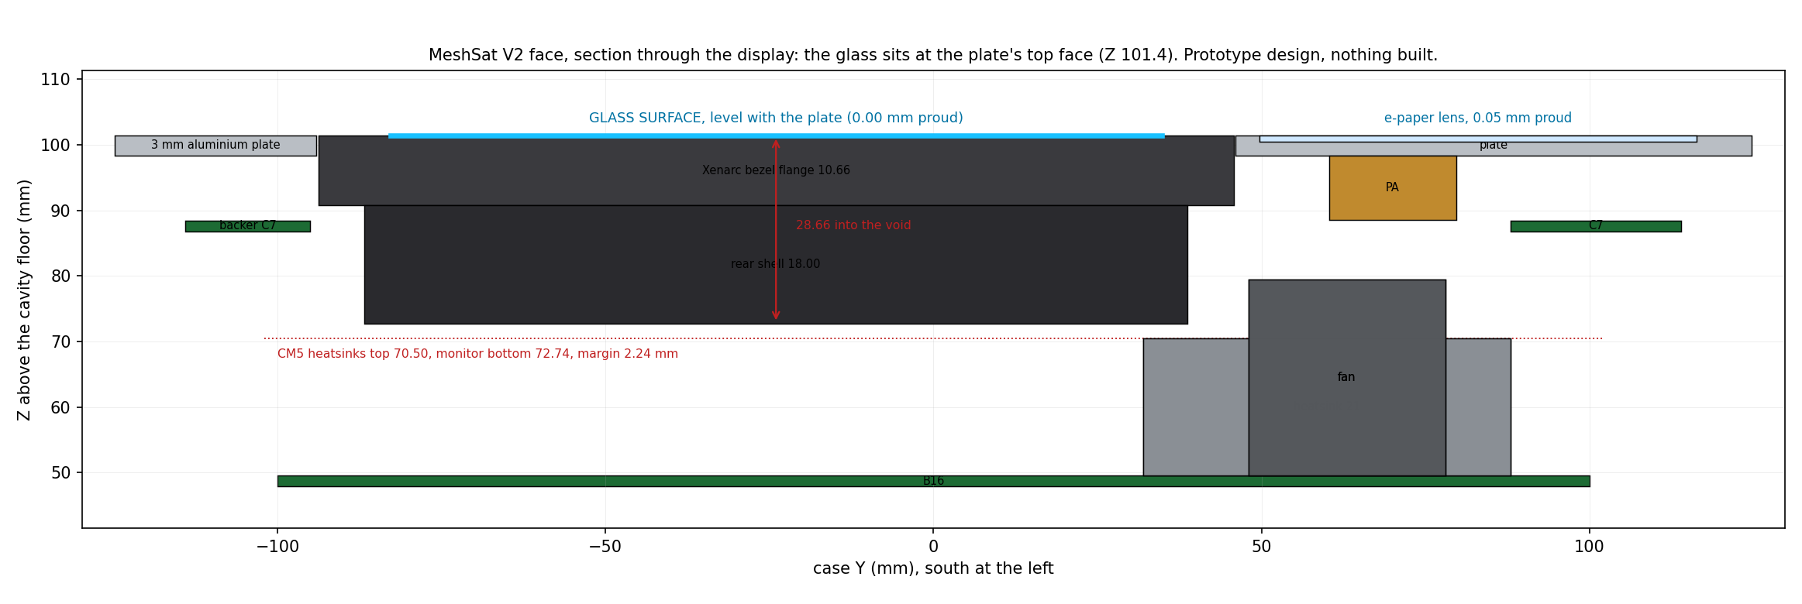
v2/images/face-section.png
