meshsat/meshsat-fieldkit/v2/release/revA/boards/meshsat-pcb-b-revA-B19-quote/pcb-b-compute-render-bottom.png

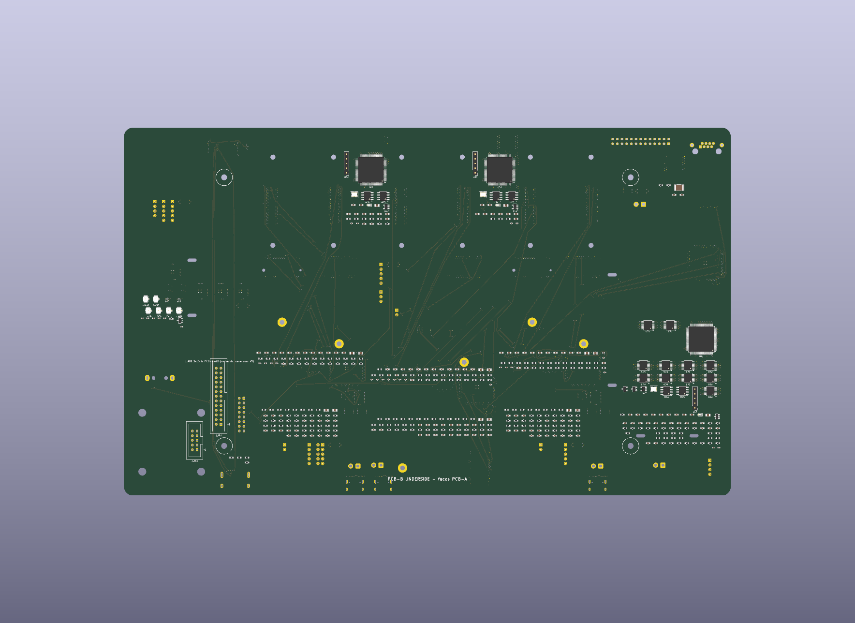
v2/release/revA/boards/meshsat-pcb-b-revA-B19-quote/pcb-b-compute-render-bottom.png
