meshsat/meshsat-fieldkit/v2/release/revA/boards/meshsat-pcb-b-revA-B19-quote/pcb-b-compute-render-top.png

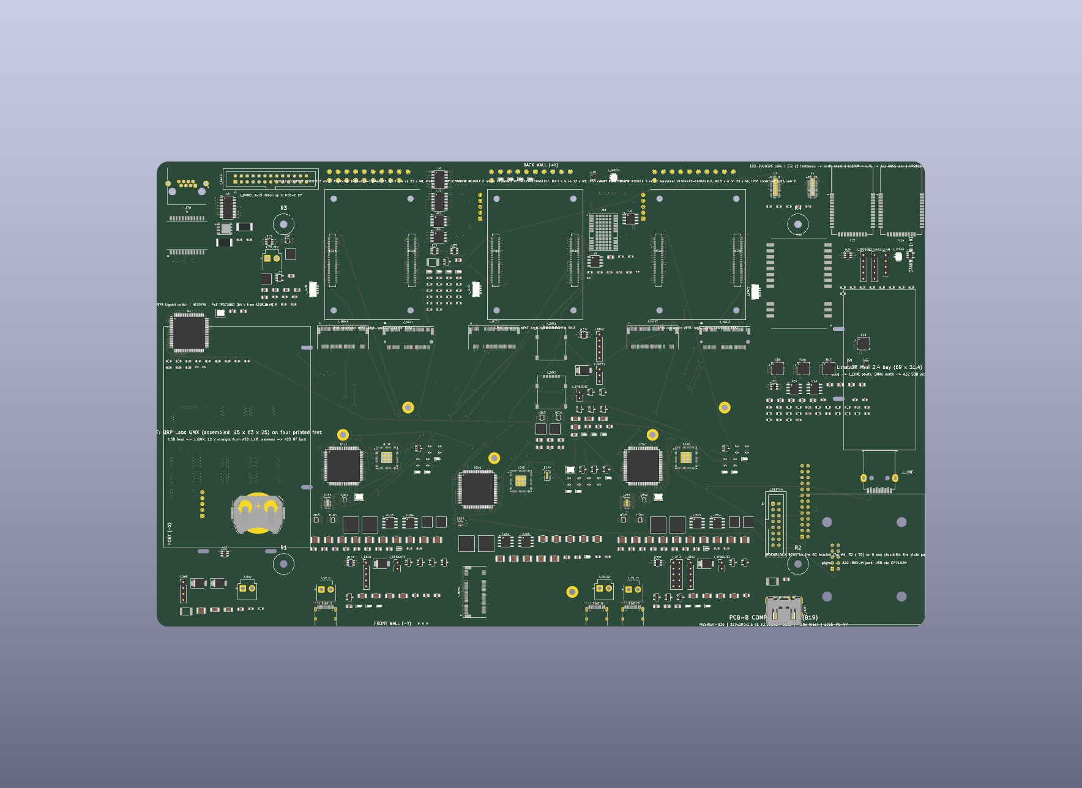
v2/release/revA/boards/meshsat-pcb-b-revA-B19-quote/pcb-b-compute-render-top.png
