meshsat/meshsat-fieldkit/v2/release/revA/boards/meshsat-pcb-c-revA-C24/pcb-c-display-render-bottom.png

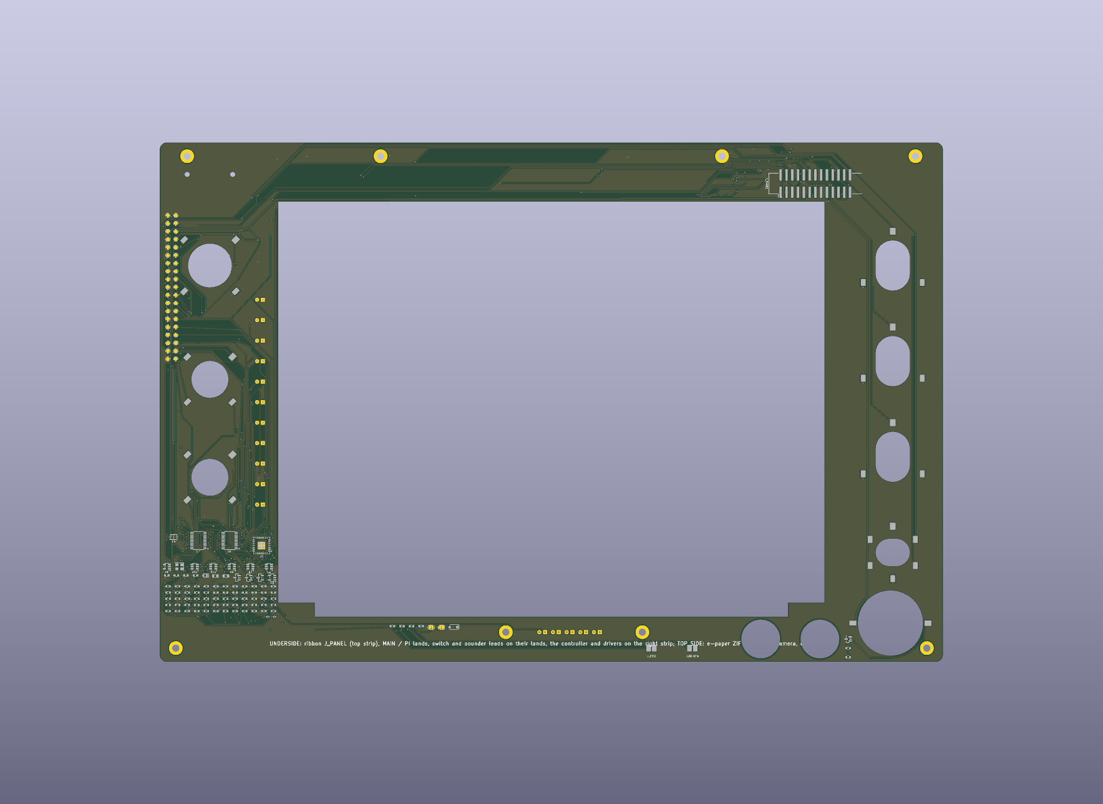
v2/release/revA/boards/meshsat-pcb-c-revA-C24/pcb-c-display-render-bottom.png
