meshsat/meshsat-fieldkit/v2/release/revA/boards/meshsat-pcb-c-ring-revA-R1/pcb-c-ring-render-bottom.png

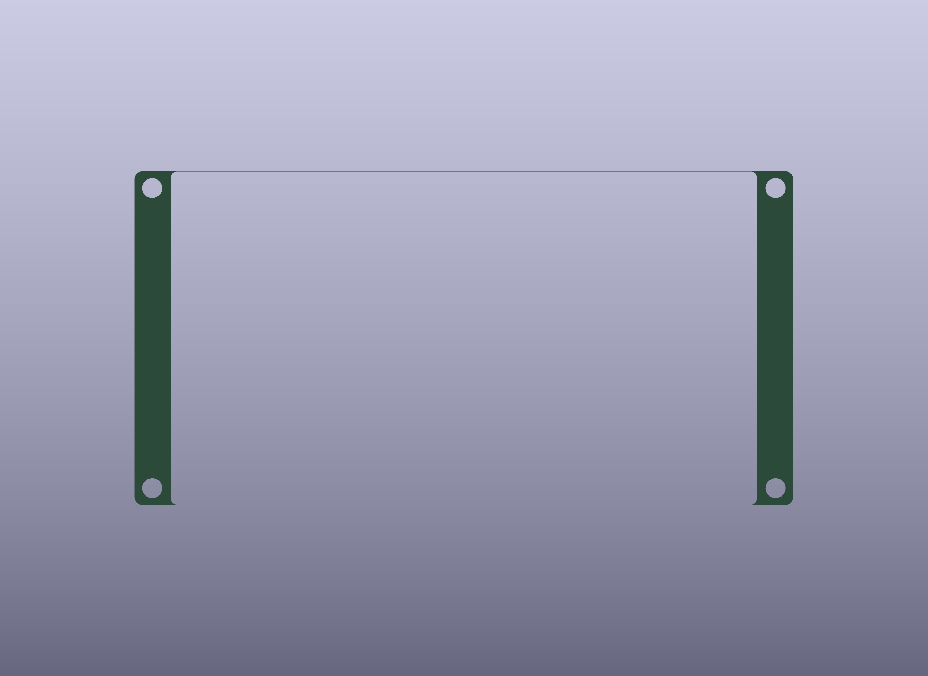
v2/release/revA/boards/meshsat-pcb-c-ring-revA-R1/pcb-c-ring-render-bottom.png
