meshsat/meshsat-fieldkit/v2/release/revA/boards/meshsat-pcb-d-revA-D11/pcb-d-aprs-render-top.png

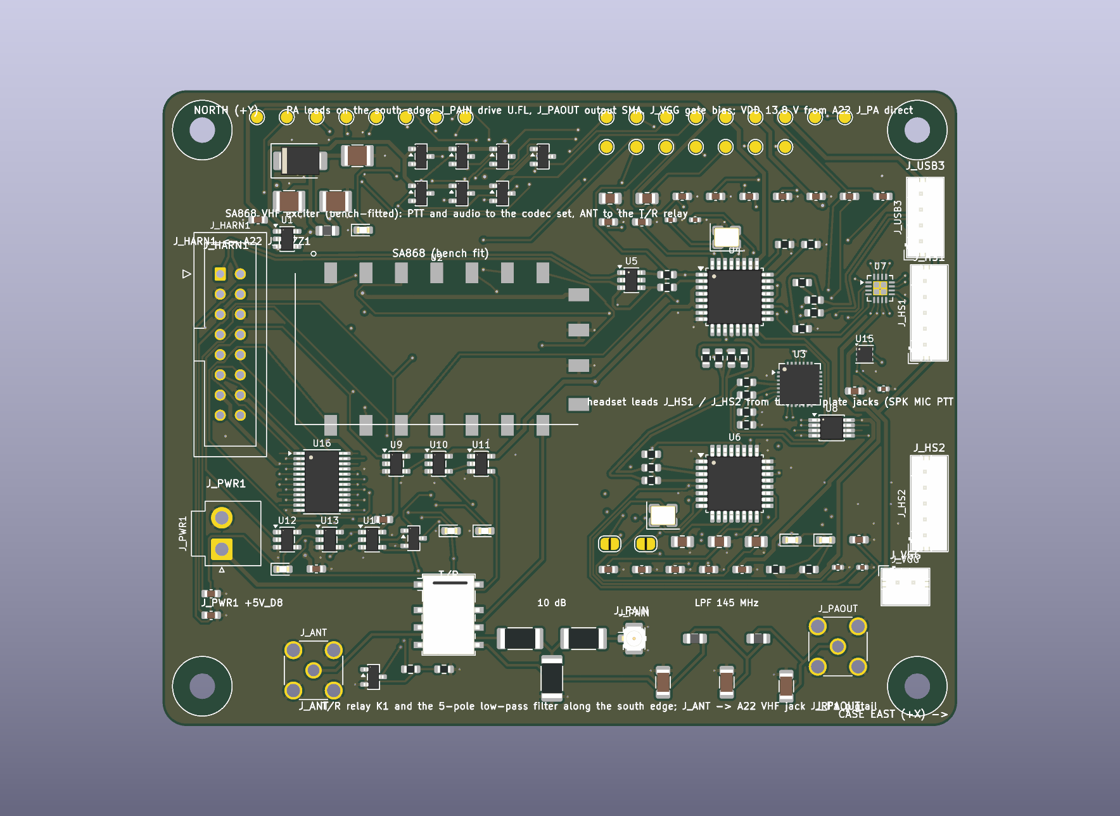
v2/release/revA/boards/meshsat-pcb-d-revA-D11/pcb-d-aprs-render-top.png
