meshsat/meshsat-fieldkit/v2/release/revA/boards/meshsat-pcb-e2-revA-E3/pcb-e2-rfjunction-render-bottom.png

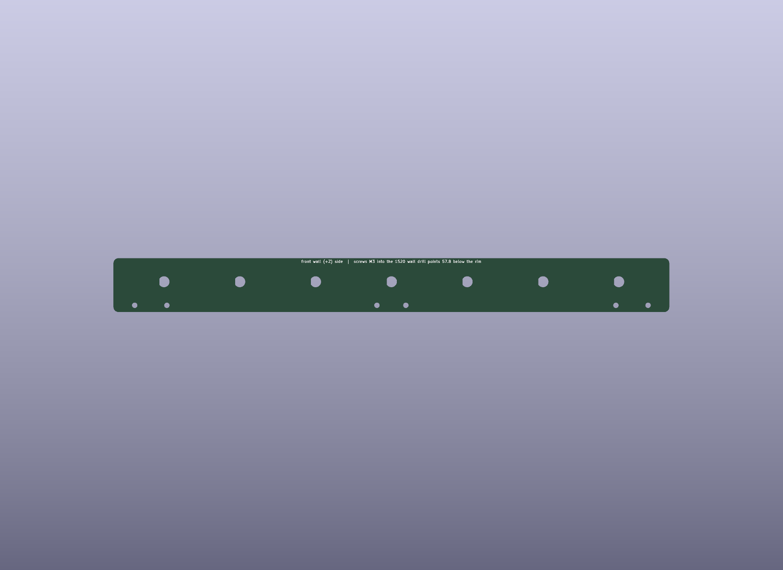
v2/release/revA/boards/meshsat-pcb-e2-revA-E3/pcb-e2-rfjunction-render-bottom.png
