meshsat/meshsat-fieldkit/v2/release/revA/boards/meshsat-pcb-e5-revA-E5/pcb-e5-block-render-bottom.png

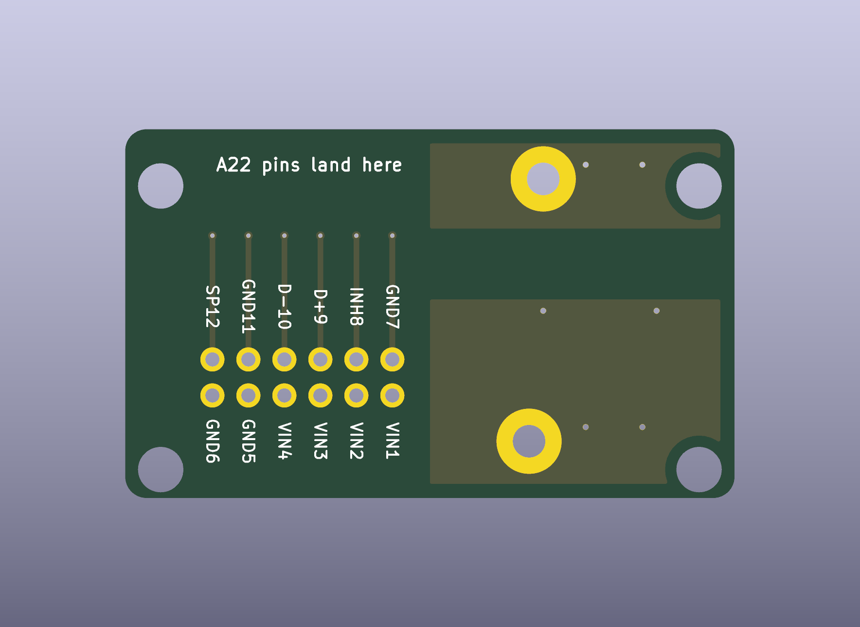
v2/release/revA/boards/meshsat-pcb-e5-revA-E5/pcb-e5-block-render-bottom.png
