meshsat/meshsat-fieldkit/v2/release/revA/boards/meshsat-pcb-p-revA-P4/pcb-p-pack-render-bottom.png

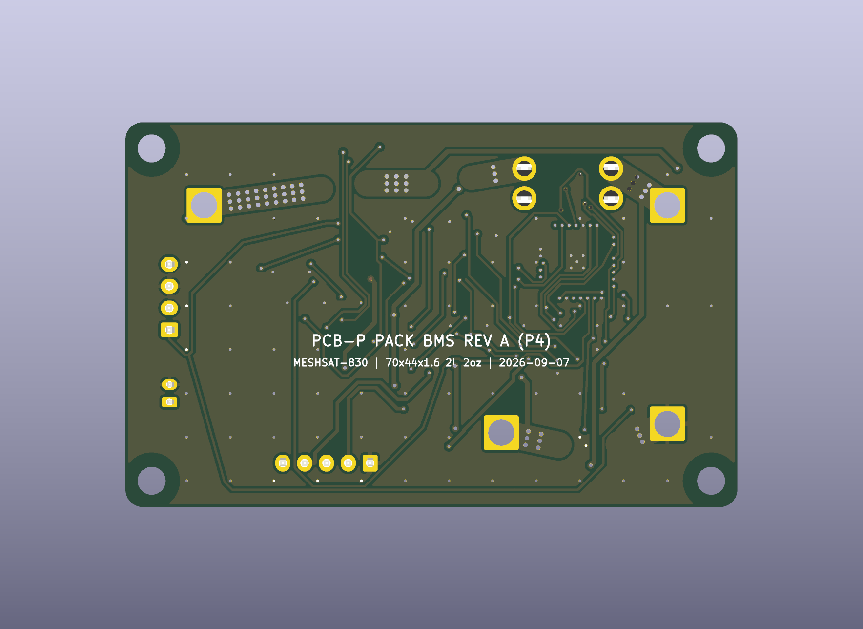
v2/release/revA/boards/meshsat-pcb-p-revA-P4/pcb-p-pack-render-bottom.png
