meshsat/meshsat-fieldkit/v2/release/revA/review/PCB-A-POWER-A22/pcb-a-power-render-bottom-A4.png

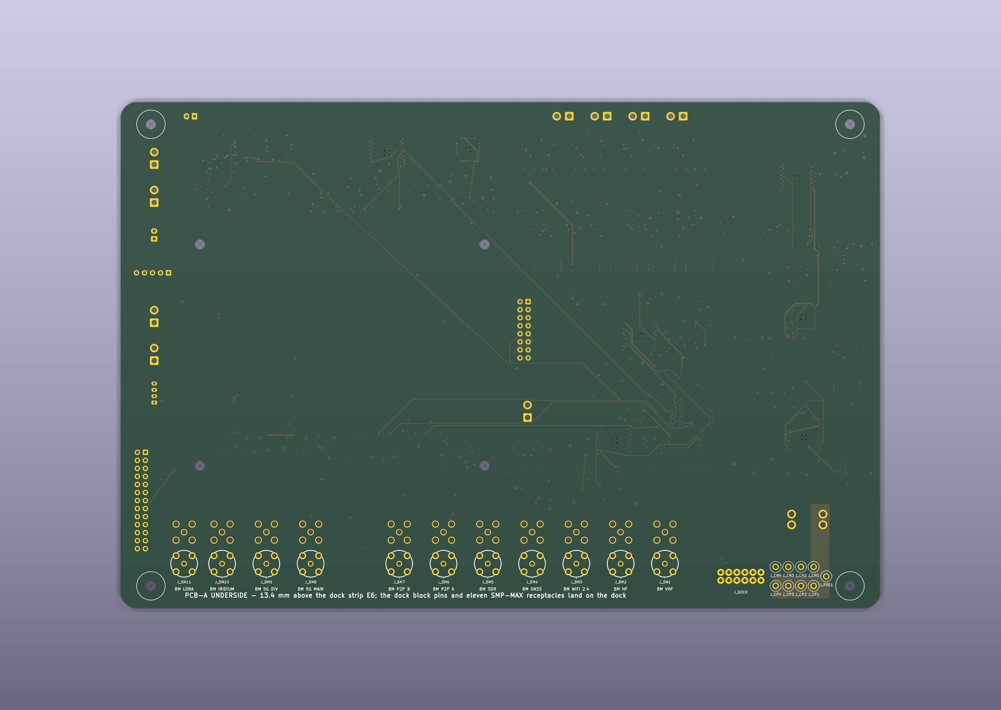
v2/release/revA/review/PCB-A-POWER-A22/pcb-a-power-render-bottom-A4.png
