meshsat/meshsat-fieldkit/v2/release/revA/review/PCB-B-COMPUTE-B16/pcb-b-compute-render-bottom-A4.png

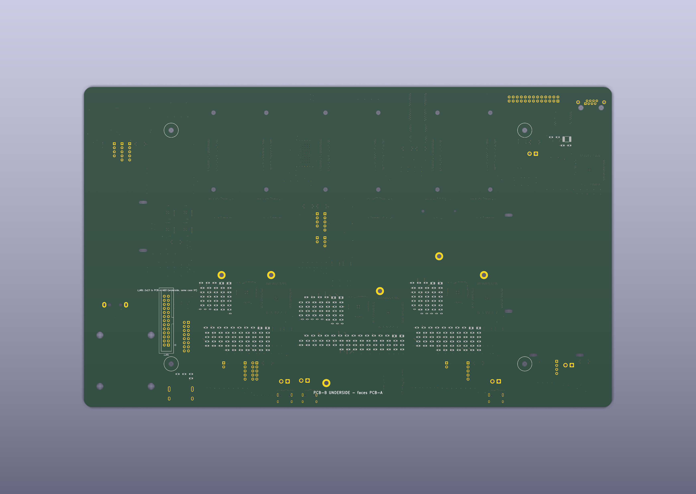
v2/release/revA/review/PCB-B-COMPUTE-B16/pcb-b-compute-render-bottom-A4.png
