meshsat/meshsat-fieldkit/v2/release/revA/review/PCB-B-COMPUTE-B16/pcb-b-compute-render-top.png

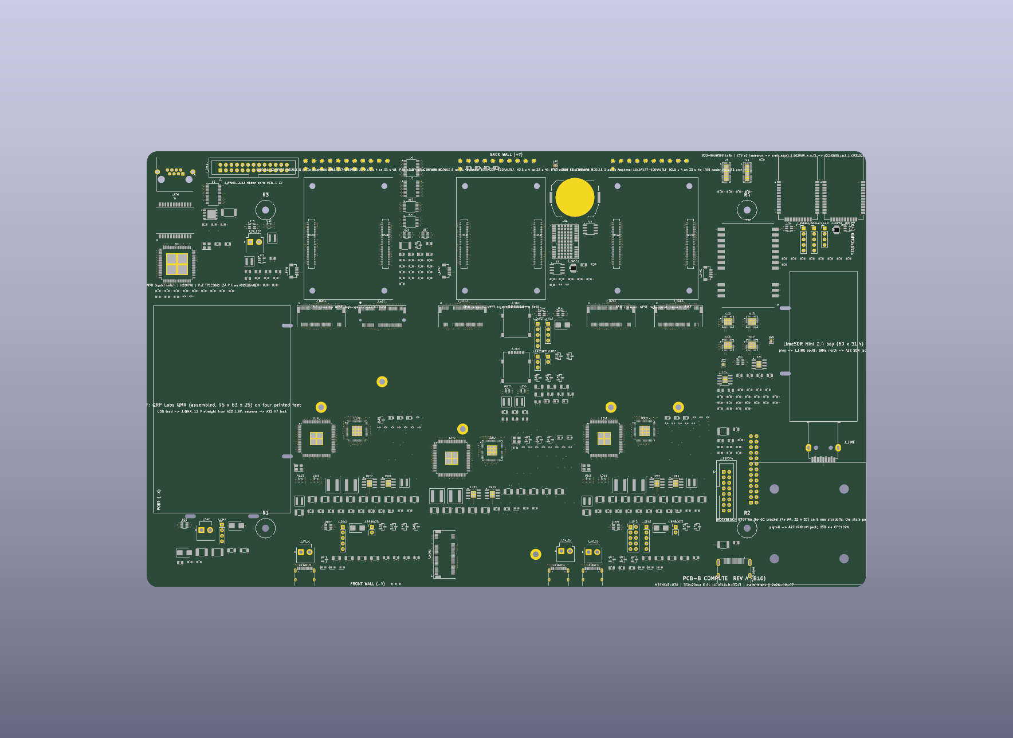
v2/release/revA/review/PCB-B-COMPUTE-B16/pcb-b-compute-render-top.png
