meshsat/meshsat-fieldkit/v2/release/revA/review/PCB-C-DISPLAY-C7/pcb-c-display-render-bottom-A4.png

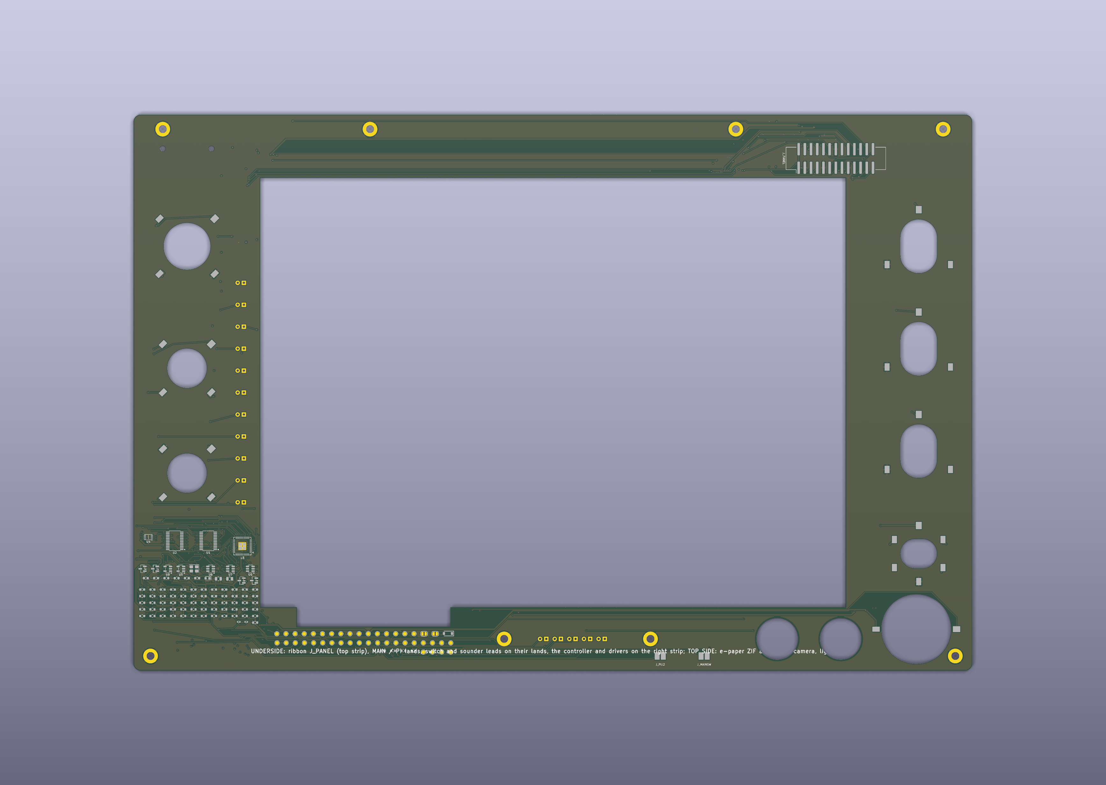
v2/release/revA/review/PCB-C-DISPLAY-C7/pcb-c-display-render-bottom-A4.png
