meshsat/meshsat-fieldkit/v2/release/revA/review/PCB-D-APRS-D8/pcb-d-aprs-render-bottom-A4.png

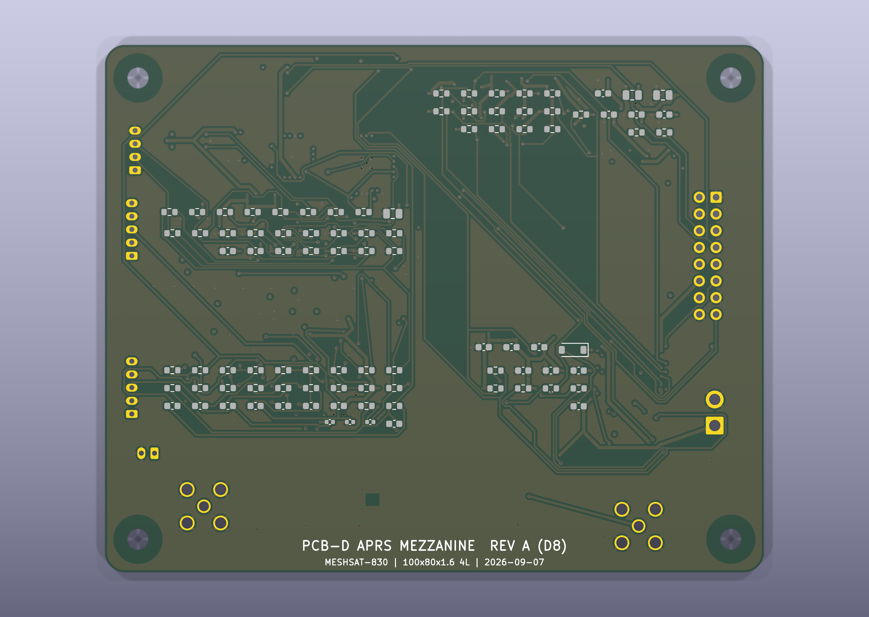
v2/release/revA/review/PCB-D-APRS-D8/pcb-d-aprs-render-bottom-A4.png
