meshsat/meshsat-fieldkit/v2/release/revA/review/PCB-E1-DOCK-E6/pcb-e1-dock-render-bottom-A4.png

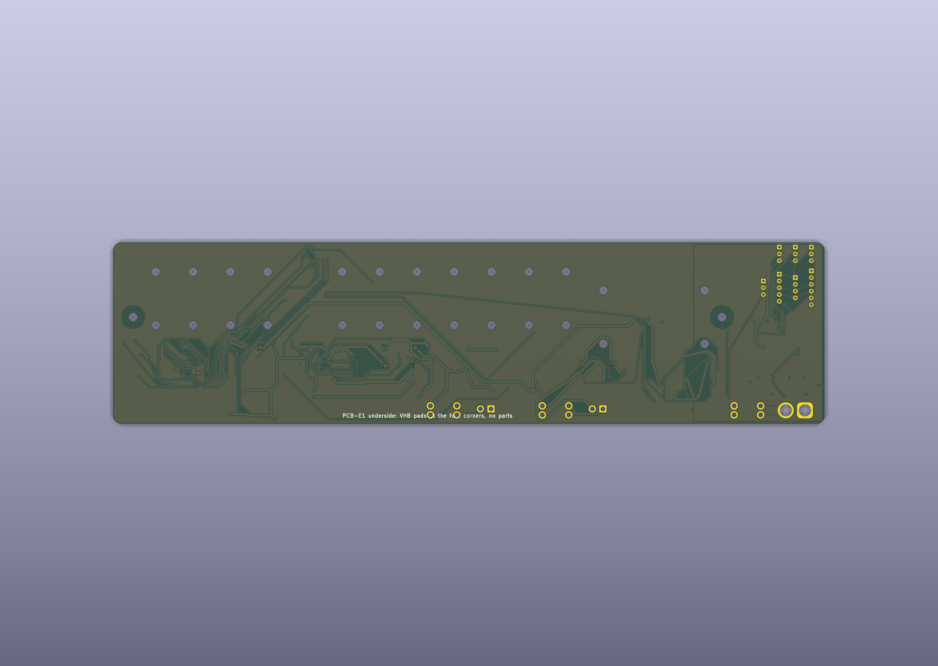
v2/release/revA/review/PCB-E1-DOCK-E6/pcb-e1-dock-render-bottom-A4.png
