meshsat/meshsat-fieldkit/v2/release/revA/review/PCB-E5-BLOCK-E5/pcb-e5-block-render-bottom-A4.png

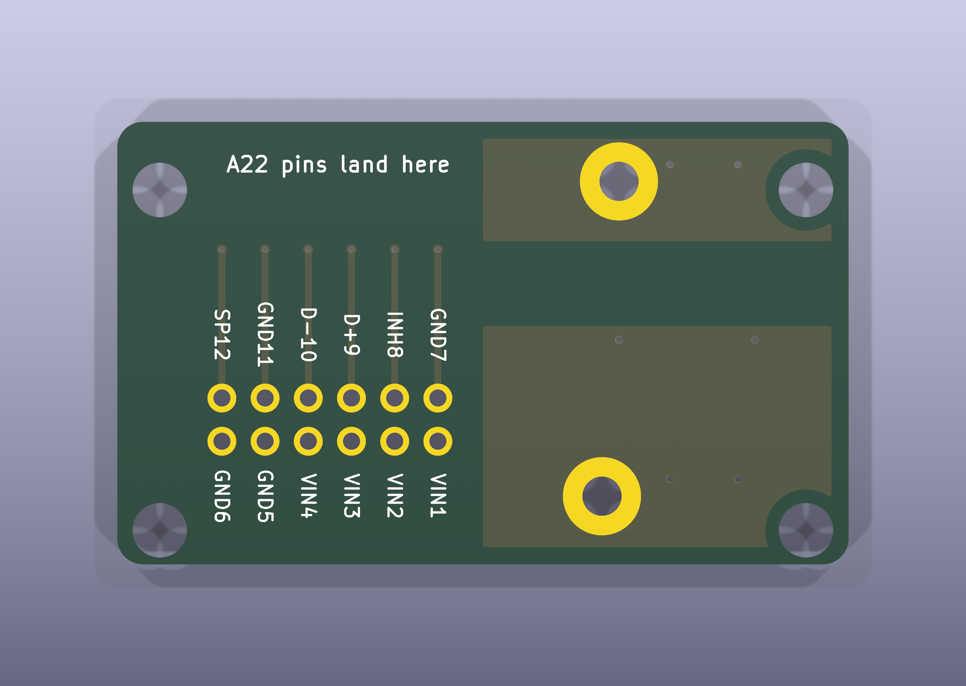
v2/release/revA/review/PCB-E5-BLOCK-E5/pcb-e5-block-render-bottom-A4.png
