meshsat/meshsat-fieldkit/v2/release/revA/review/PCB-P-PACK-P1/pcb-p-pack-render-bottom-A4.png

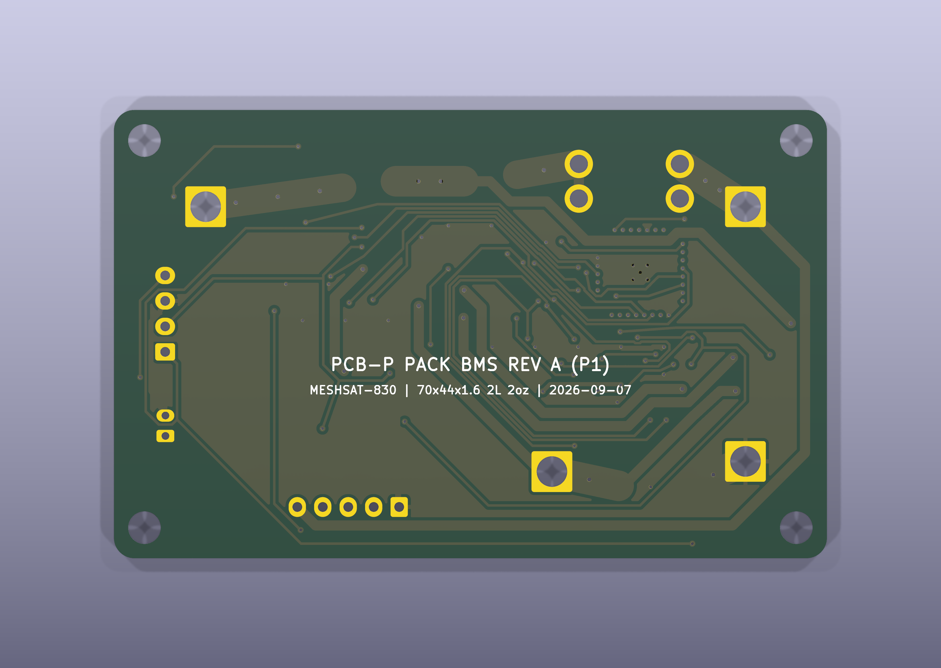
v2/release/revA/review/PCB-P-PACK-P1/pcb-p-pack-render-bottom-A4.png
