meshsat/meshsat-fieldkit/v2/release/revA/order/README.md

# MeshSat field-kit carrier boards, JLCPCB order set (generated 2026-09-26 07:25)

<!-- readiness:begin (generated by tools/order_readiness.py; do not edit) -->
**QUARANTINED: nothing in this folder is an approved fabrication package, and nothing is ordered from it** (owner decision 41, 25 September 2026). Every `ORDER-NOTES.txt` opens with its board's readiness in the four fields below; read it before anything else. A folder whose phase is not the phase its board declares is an older board than the one this project is building.

| Folder | Board | Folder phase | Board declares | ROUTING_STATUS | ELECTRICAL_PROTECTION_STATUS | FAB_READINESS | PUBLICATION_STATUS |
|---|---|---|---|---|---|---|---|
| `PCB-A-POWER-A22/` | A | A22 | A32 | OPEN | BLOCKED_DECISION_31 | NOT_READY | HELD |
| `PCB-B-COMPUTE-B16/` | B | B16 | B21 | FAIL | PASS | NOT_READY | NOT_RELEASED |
| `PCB-C-DISPLAY-C24/` | C | C24 | C24 | PASS | PASS | NOT_READY | NOT_RELEASED |
| `PCB-D-APRS-D8/` | D | D8 | D12 | PASS | BLOCKED_DECISION_31 | NOT_READY | HELD |
| `PCB-E1-DOCK-E6/` | E | E6 | E17 | PASS | BLOCKED_DECISION_31 | NOT_READY | HELD |
| `PCB-E5-BLOCK-E5/` | E5 | E5 | E5 | PASS | PASS | NOT_READY | NOT_RELEASED |
| `PCB-P-PACK-P4/` | P | P4 | P4 | FAIL | FAIL | NOT_READY | NOT_RELEASED |
<!-- readiness:end -->

One sub-folder per board. Upload the Gerber zip first, then (for the assembled boards) the BOM and CPL files in the assembly step.

| Folder | Board | Size | Layers | Assembly | Files |
|---|---|---|---|---|---|
| `PCB-A-POWER-A22/` | PCB-A POWER + I/O Rev A (A22) | 240 x 160 mm | 6 | top 343 + bottom 0 parts, 0 DNP removed | pcb-a-power-gerbers.zip, pcb-a-power-bom.csv, pcb-a-power-cpl.csv |
| `PCB-B-COMPUTE-B16/` | PCB-B COMPUTE Rev A (B16) QUOTE ONLY, unrouted pre-route board | 330 x 200 mm | 6 | top 412 + bottom 303 parts, 0 DNP removed | pcb-b-compute-gerbers.zip, pcb-b-compute-bom.csv, pcb-b-compute-cpl.csv |
| `PCB-C-DISPLAY-C24/` | PCB-C PANEL BACKER Rev A (C24) | 344 x 228 mm | 4 | top 37 + bottom 93 parts, 0 DNP removed | pcb-c-display-gerbers.zip, pcb-c-display-bom.csv, pcb-c-display-cpl.csv |
| `PCB-D-APRS-D8/` | PCB-D APRS MEZZANINE Rev A (D8) | 100 x 80 mm | 4 | top 88 + bottom 92 parts, 0 DNP removed | pcb-d-aprs-gerbers.zip, pcb-d-aprs-bom.csv, pcb-d-aprs-cpl.csv |
| `PCB-E1-DOCK-E6/` | PCB-E1 DOCK STRIP Rev A (E6) | 267 x 68 mm | 4 | top 138 + bottom 0 parts, 0 DNP removed | pcb-e1-dock-gerbers.zip, pcb-e1-dock-bom.csv, pcb-e1-dock-cpl.csv |
| `PCB-E5-BLOCK-E5/` | PCB-E5 DOCK BLOCK Rev A (E5) | 43 x 26 mm | 2 | none (PCB only) | pcb-e5-block-gerbers.zip |
| `PCB-P-PACK-P4/` | PCB-P PACK BMS Rev A (P4) | 70 x 44 mm | 2 | top 42 + bottom 0 parts, 0 DNP removed | pcb-p-pack-gerbers.zip, pcb-p-pack-bom.csv, pcb-p-pack-cpl.csv |

Common options for all boards: ENIG, matte black mask, white silk. The copper weight, the layer count and the stackup are each board's own, read from its board file into its ORDER-NOTES.txt.
The BOM/CPL copies here have the DNP and bench-fitted lines removed; each board's ORDER-NOTES.txt lists its own designators by name, and the full BOMs stay in the deliverable folders.
Nothing here is ordered and no folder here is approved: an order is placed only by the owner, after the board is promoted. The readiness of each folder is the block at the top of its ORDER-NOTES.txt and the table above.

**`ROTATION-CHECKLIST.md` is this folder's work list for the ordering session (generated 18 September 2026 by `tools/assembly_set.py --checklist`; regenerate it, never edit it).** Rule DFA-001 asks that every polarised part's rotation be verified against the assembler's own convention with the verification DATED, and it reads INCONCLUSIVE on all seven boards for one reason: **42 polarised footprints reach the assembler with KiCad's rotation unchanged and nobody has compared them with the assembler's 2D preview.** Only the ordering session has that preview. Each row carries the footprint, the boards that place it and one designator to look up; an offset of zero is a real answer and is recorded the same way, because what the rule refuses is the blank. The verified rows live in `jlc-rotations.csv` with their date.
