meshsat/meshsat-fieldkit/v2/release/revA/order/ORDER-LOG.md

# ORDER-LOG.md: JLCPCB ordering of the MeshSat field-kit carrier boards (MESHSAT-709)

Order session started 2026-09-03. Operator: Claude Code on the laptop via the Chrome extension, JLCPCB account already logged in. Nothing is paid by this session; every board stops at the cart. The order gate is the 12 Sep review with Nick and the owner's "order now".

## 1. Intake checks (step 1 of the method), 2026-09-03

Inputs read: all six ORDER-NOTES.txt, README.md, ASSEMBLY.md section 9 (bench-fit lists). Gerber zips in `JLCPCB/` are byte-identical to the ones in the deliverable folders (cmp).

### 1.1 BLOCKING: the three 4-layer zips contain no inner copper layers

| Board | Notes say | Zip contains | KiCad board |
|---|---|---|---|
| PCB-A-POWER-A15 | 4 layers, JLC04161H-7628 | F_Cu, B_Cu only (no In1/In2) | 4 copper layers, 463 items reference In1.Cu, 306 reference In2.Cu |
| PCB-B-COMPUTE-B10 | 4 layers, JLC04161H-7628 | F_Cu, B_Cu only | 4 copper layers, 582 on In1.Cu, 520 on In2.Cu |
| PCB-D-APRS-D5 | 4 layers, JLC04161H-7628 | F_Cu, B_Cu only | 4 copper layers, 229 on In1.Cu, 169 on In2.Cu |

Every zip holds exactly 11 files: F/B copper, mask, paste, silk, Edge_Cuts, .drl and the drill map. The inner layers were not exported. Uploading these three zips as 4-layer would order boards without their planes and inner routing. NOT uploaded. The gerbers must be re-exported with In1.Cu and In2.Cu included (kicad-cli is on this laptop at /usr/bin/kicad-cli; the session rule "never touch the KiCad projects or the generators" means the re-export is the owner's or the design session's call). The 2-layer boards (C3, E1, E2) are complete and proceed.

Also noted: `meshsat-pcb-a-revA-A15/README-fab.txt` carries the PCB-B text (title, size, connector). Cosmetic, the ORDER-NOTES.txt for A15 is correct and wins.

### 1.2 BOM designator format (fixed in upload copies, originals untouched)

JLC's BOM parser expects comma-separated designators. The generated BOMs use range notation (`C34-C37`, `R16-R22`) and KiCad's unannotated marker `?` on every non-numeric reference (`J_DOCK?`, `SW_MAIN?`), while the CPL carries the expanded plain names. Left as is, every such line would fail to pair with its CPL row. Cleaned copies were written to `<board>/upload/` with: ranges expanded, `?` stripped, solder-jumper lines (JPx: pads, no part, absent from the CPL) dropped, and the bench-fitted items from ORDER-NOTES / ASSEMBLY.md section 9 removed from BOM and CPL. After cleaning, the BOM designator set equals the CPL designator set on every board.

### PCB-A-POWER-A15
- Upload copies written to `PCB-A-POWER-A15/upload/` (originals untouched).
- Designator ranges expanded (4 BOM lines): C18,C20,C22,C24,C26,C28,C30,C32,C34-C37; R12,R20-R23,R26,R28,R30,R32,R34; R35-R38; R39-R43
- Trailing "?" stripped (KiCad unannotated marker on non-numeric references, the CPL carries the plain name): J_DOCK?, J_PACK?, J_X1202BAT?, J_X1202DC?
- Solder-jumper lines dropped from the BOM (PCB features, no part, not in the CPL): JP1
- Bench-fitted lines removed from BOM: J_DOCK; from CPL: J_DOCK
- Result: 30 BOM lines (13 with LCSC), 79 CPL placements (top 79, bottom 0); BOM refs == CPL refs: True

### PCB-B-COMPUTE-B10
- Upload copies written to `PCB-B-COMPUTE-B10/upload/` (originals untouched).
- Designator ranges expanded (4 BOM lines): C6,C8,C11,C29-C32; R3-R6,R13,R15,R17,R20,R25,R28,R29; R9-R12; R27,R30-R35
- Trailing "?" stripped (KiCad unannotated marker on non-numeric references, the CPL carries the plain name): J_PANEL?
- Solder-jumper lines dropped from the BOM (PCB features, no part, not in the CPL): JP1, JP3, JP4
- Bench-fitted lines removed from BOM: none; from CPL: none
- Result: 41 BOM lines (16 with LCSC), 113 CPL placements (top 112, bottom 1); BOM refs == CPL refs: True

### PCB-C-DISPLAY-C3
- Upload copies written to `PCB-C-DISPLAY-C3/upload/` (originals untouched).
- Designator ranges expanded (8 BOM lines): C3,C4,C11-C13; C5-C10; Q2-Q4; R1-R5,R7,R8; R11,R34-R38; R13-R15,R23,R28,R32; R16-R22,R24-R27; U5-U8
- Trailing "?" stripped (KiCad unannotated marker on non-numeric references, the CPL carries the plain name): J_EPD?, J_PANEL?, J_X1202SW?, SW_EMCON?, SW_LIGHT?, SW_MAIN?, SW_PI?, SW_SOS?, SW_TEST?, SW_ZERO?
- Solder-jumper lines dropped from the BOM (PCB features, no part, not in the CPL): JP1, JP2
- Bench-fitted lines removed from BOM: SW_EMCON, SW_LIGHT, SW_MAIN, SW_PI, SW_SOS, SW_TEST, SW_ZERO; from CPL: EPD1, SW_EMCON, SW_LIGHT, SW_MAIN, SW_PI, SW_SOS, SW_TEST, SW_ZERO
- Result: 40 BOM lines (19 with LCSC), 88 CPL placements (top 18, bottom 70); BOM refs == CPL refs: True

### PCB-D-APRS-D5
- Upload copies written to `PCB-D-APRS-D5/upload/` (originals untouched).
- Designator ranges expanded (3 BOM lines): C4-C7,C10,C13,C14,C31; C8,C9,C12,C15-C18,C25,C32; C26-C29
- Trailing "?" stripped (KiCad unannotated marker on non-numeric references, the CPL carries the plain name): none
- Solder-jumper lines dropped from the BOM (PCB features, no part, not in the CPL): JP1, JP2, JP3, JP4, JP5
- Bench-fitted lines removed from BOM: none; from CPL: none
- Result: 39 BOM lines (21 with LCSC), 77 CPL placements (top 76, bottom 1); BOM refs == CPL refs: True
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
