meshsat/meshsat-fieldkit/v2/docs/records/d6rel/inventory-before-after.txt

THE INVENTORY OF REL-001 ON THE SET 6 ARTEFACTS, BEFORE AND AFTER (worker d6rel, MESHSAT-1357, taken 28 September 2026 17:55 CEST, after the fixes of the fresh check)
Written by v2/docs/records/d6rel/measure_inventory.py (read only; the old list is git show 73ae2f21:v2/ecad/tools/pcb_reliability.yaml written to $SP/old/):
  python3 v2/docs/records/d6rel/measure_inventory.py v2/ecad/tools --old $SP/old
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
