meshsat/meshsat-fieldkit/v2/release/revA/order/cart-830-set-2026-09-08.jpg

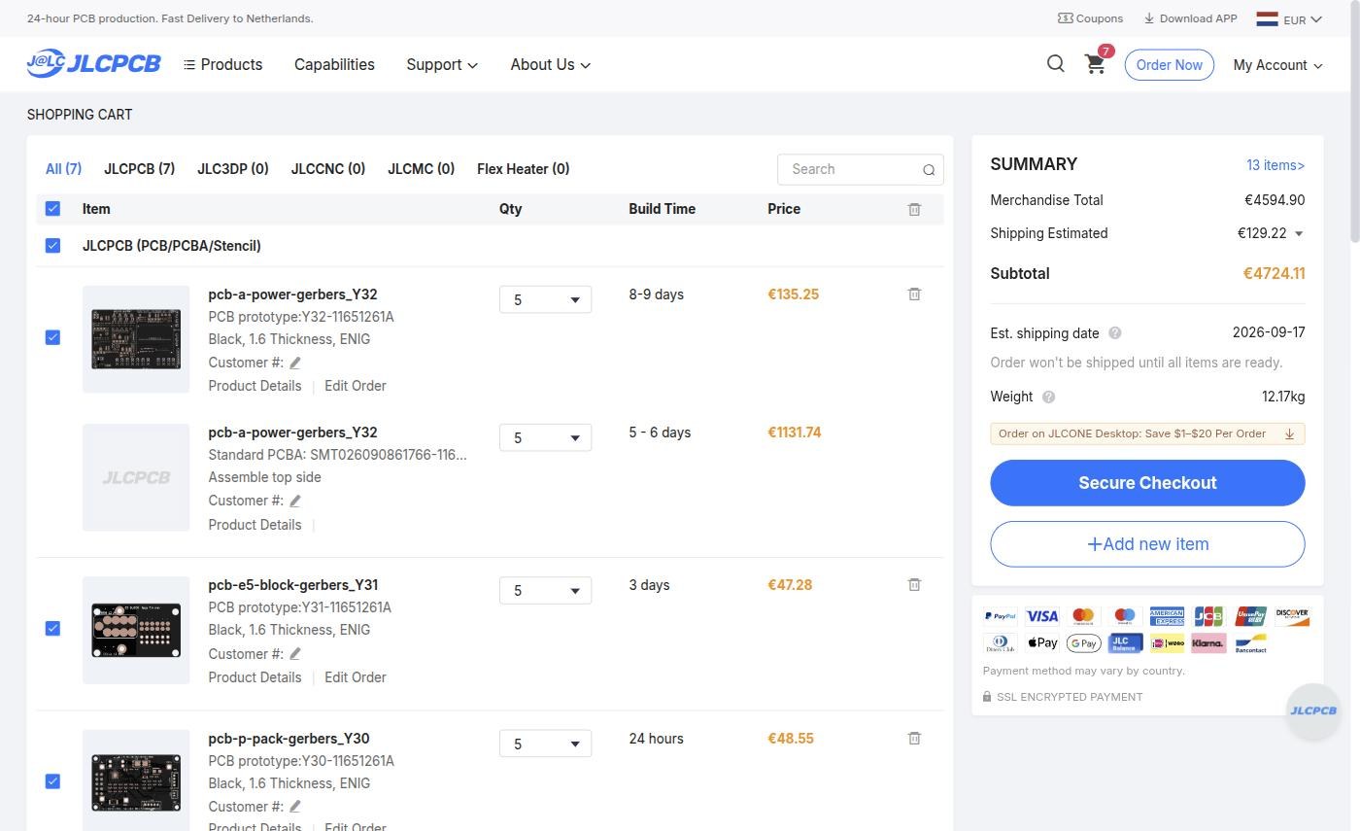
v2/release/revA/order/cart-830-set-2026-09-08.jpg
