meshsat/meshsat-fieldkit/v2/release/revA/order/cart-all-six-boards-2026-09-03.jpg

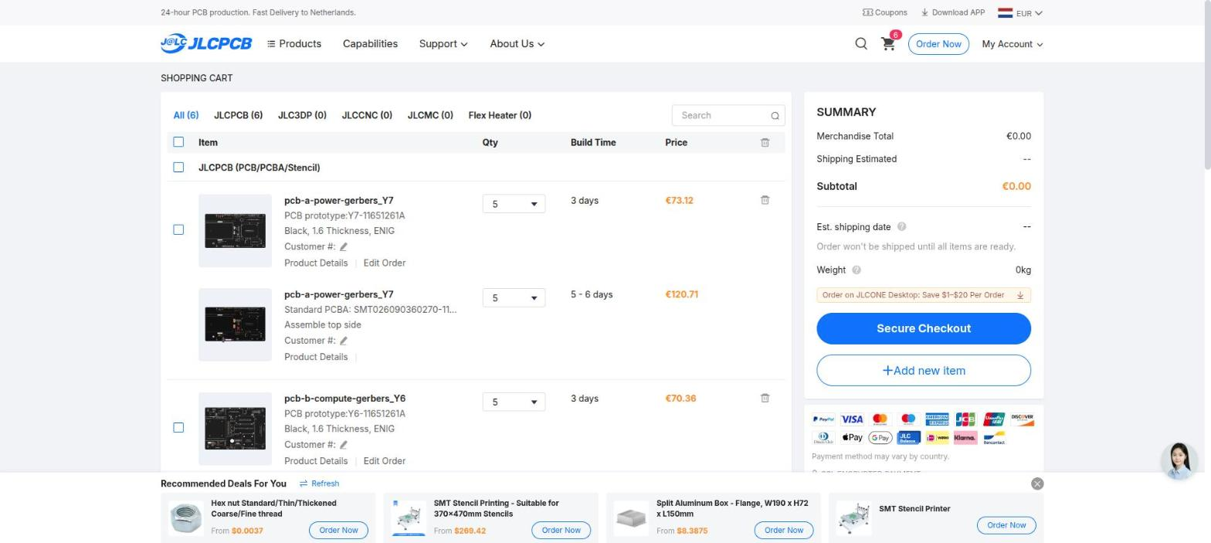
v2/release/revA/order/cart-all-six-boards-2026-09-03.jpg
