meshsat/meshsat-fieldkit/v2/release/revA/order/PCB-B-COMPUTE-B10/jlcpcb-placement-preview-bottom-2026-09-03.jpg

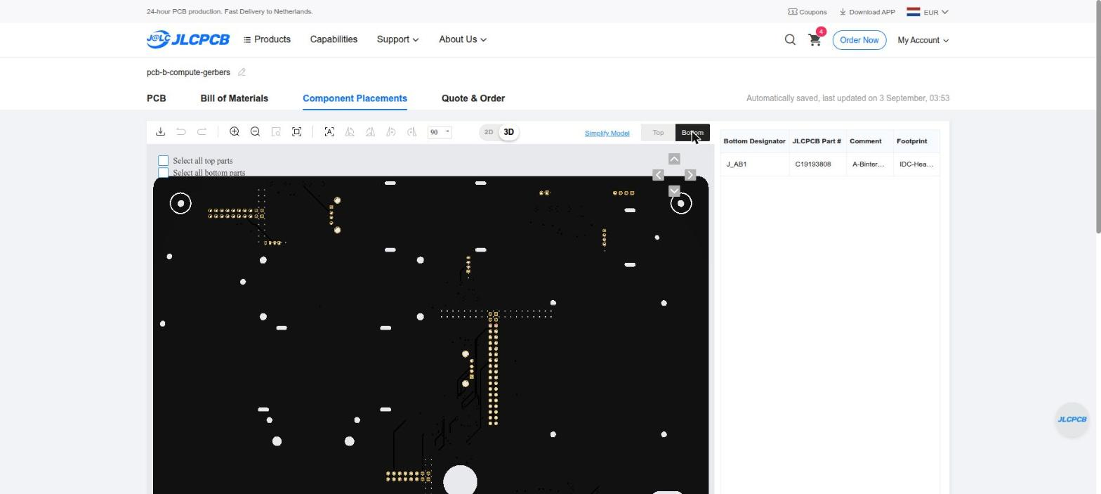
v2/release/revA/order/PCB-B-COMPUTE-B10/jlcpcb-placement-preview-bottom-2026-09-03.jpg
