meshsat/meshsat-fieldkit/v2/release/revA/order/PCB-D-APRS-D5/jlcpcb-placement-preview-top-2026-09-03.jpg

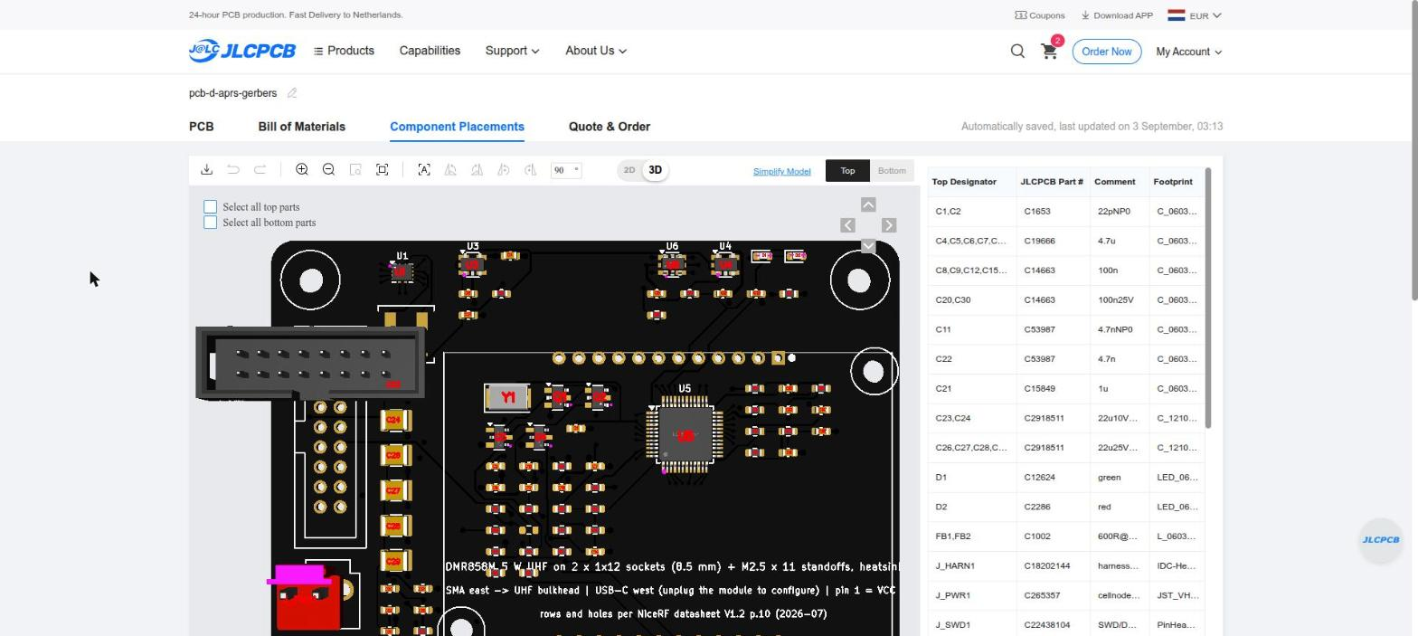
v2/release/revA/order/PCB-D-APRS-D5/jlcpcb-placement-preview-top-2026-09-03.jpg
