meshsat/meshsat-fieldkit/v2/release/revA/order/PCB-E1-DOCK-E1/jlcpcb-cart-added-2026-09-03.jpg

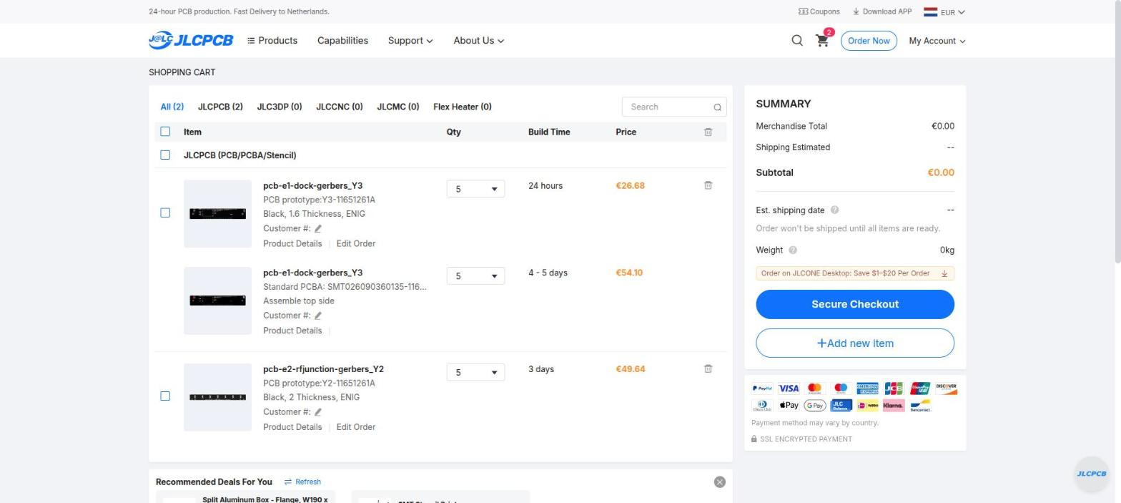
v2/release/revA/order/PCB-E1-DOCK-E1/jlcpcb-cart-added-2026-09-03.jpg
