meshsat/meshsat-fieldkit/v2/release/revA/order/PCB-E2-RFJUNCTION-E2/jlcpcb-cart-added-2026-09-03.jpg

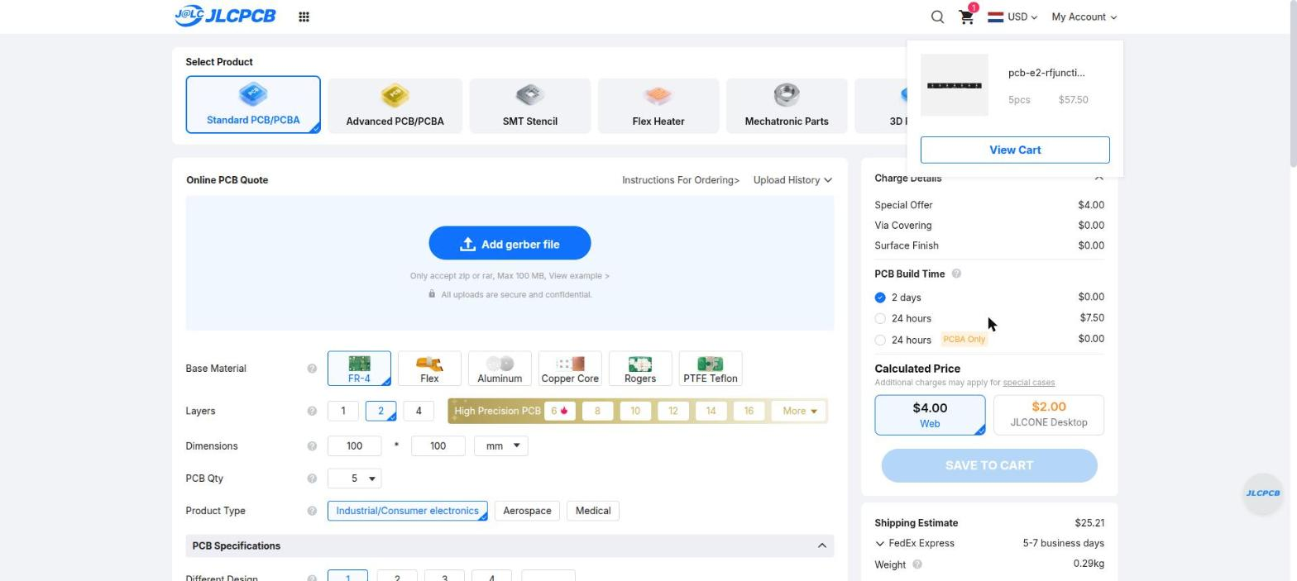
v2/release/revA/order/PCB-E2-RFJUNCTION-E2/jlcpcb-cart-added-2026-09-03.jpg
