meshsat/meshsat-fieldkit/v2/release/case-2026-09-27/rf-entry-plates/rf-entry-gasket-west.dxf

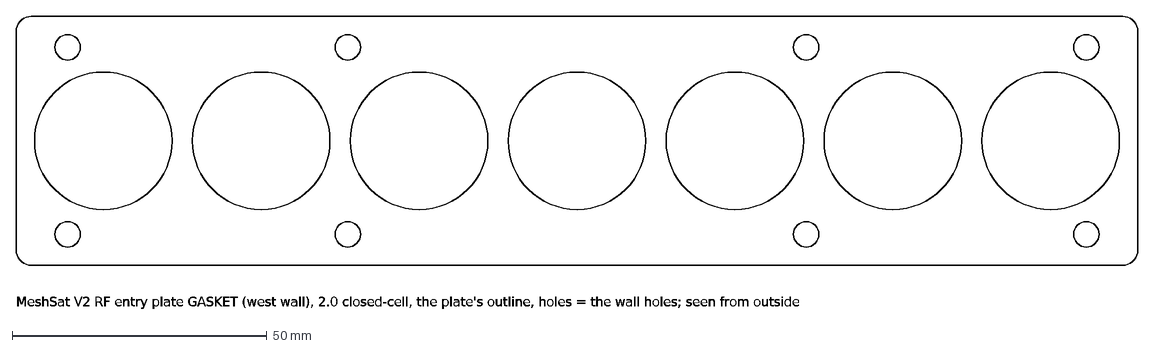
[picture p158: CAD file, 2026-09-27]
v2/release/case-2026-09-27/rf-entry-plates/rf-entry-gasket-west.dxf
MeshSat V2 RF entry plate GASKET (west wall), 2.0 closed-cell, the plate's outline, holes = the wall holes; seen from outside
