meshsat/meshsat-fieldkit/v2/release/handover/H1/v2/release/revA/case/pack-4s/pack-4s-lid.step

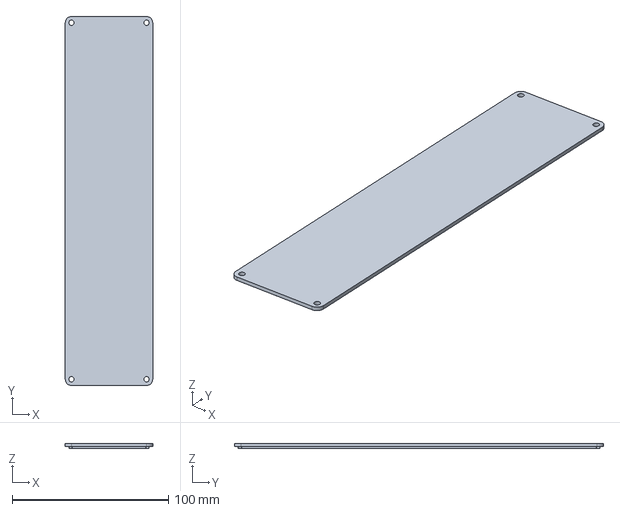
[picture p159: CAD file, 2026-09-07]
v2/release/handover/H1/v2/release/revA/case/pack-4s/pack-4s-lid.step
56.0 x 236.0 x 3.50 mm
