meshsat/meshsat-fieldkit/v2/release/handover/H1/v2/release/revA/module/battery-module-lid.step

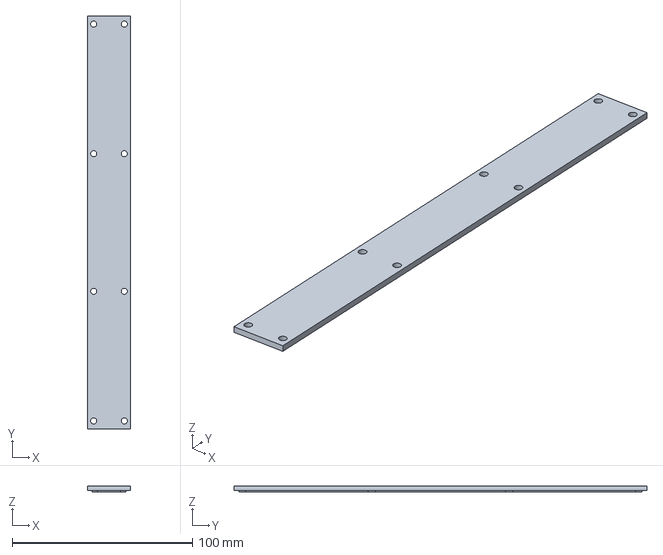
[picture p160: CAD file, 2026-09-05]
v2/release/handover/H1/v2/release/revA/module/battery-module-lid.step
24.0 x 229.2 x 3.50 mm
