meshsat/meshsat-fieldkit/v2/release/revA/boards/meshsat-pcb-c-revA-C5/pcb-c-display-seals.dxf

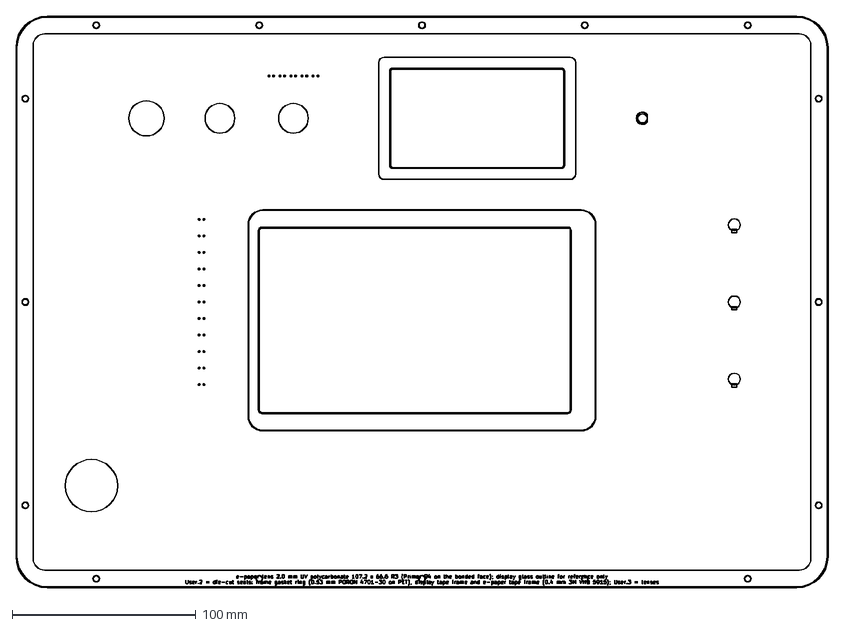
[picture p161: CAD file, 2026-09-04]
v2/release/revA/boards/meshsat-pcb-c-revA-C5/pcb-c-display-seals.dxf
442.0 x 311.0 mm
