meshsat/meshsat-fieldkit/v2/release/revA/case/face-plate/face-plate.stl

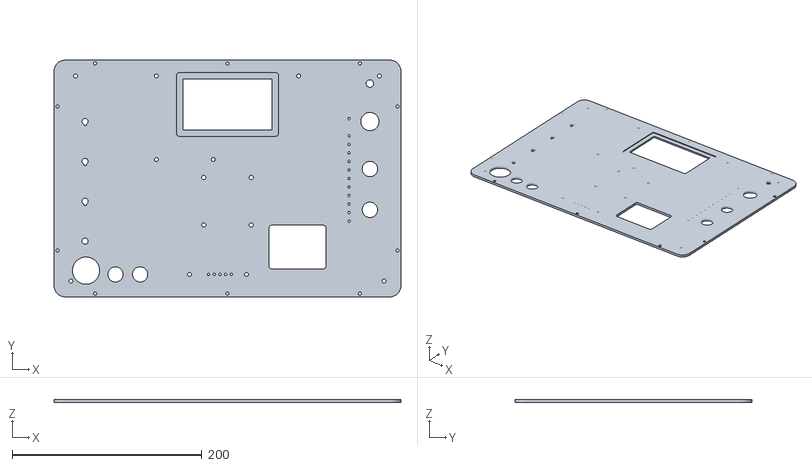
[picture p162: CAD file, 2026-09-07]
v2/release/revA/case/face-plate/face-plate.stl
365.5 x 249.5 x 3.00
