meshsat/meshsat-fieldkit/v2/release/revA/case/pack-4s/pack-4s-box.stl

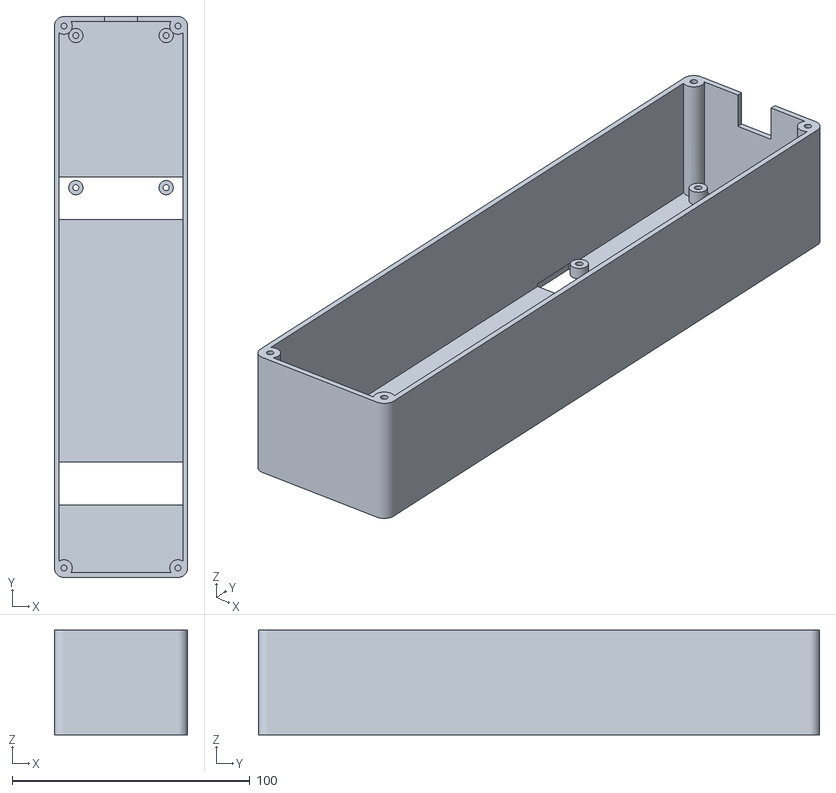
[picture p163: CAD file, 2026-09-07]
v2/release/revA/case/pack-4s/pack-4s-box.stl
56.0 x 236.0 x 44.0
