meshsat/meshsat-fieldkit/v2/release/revA/module/battery-module-base.stl

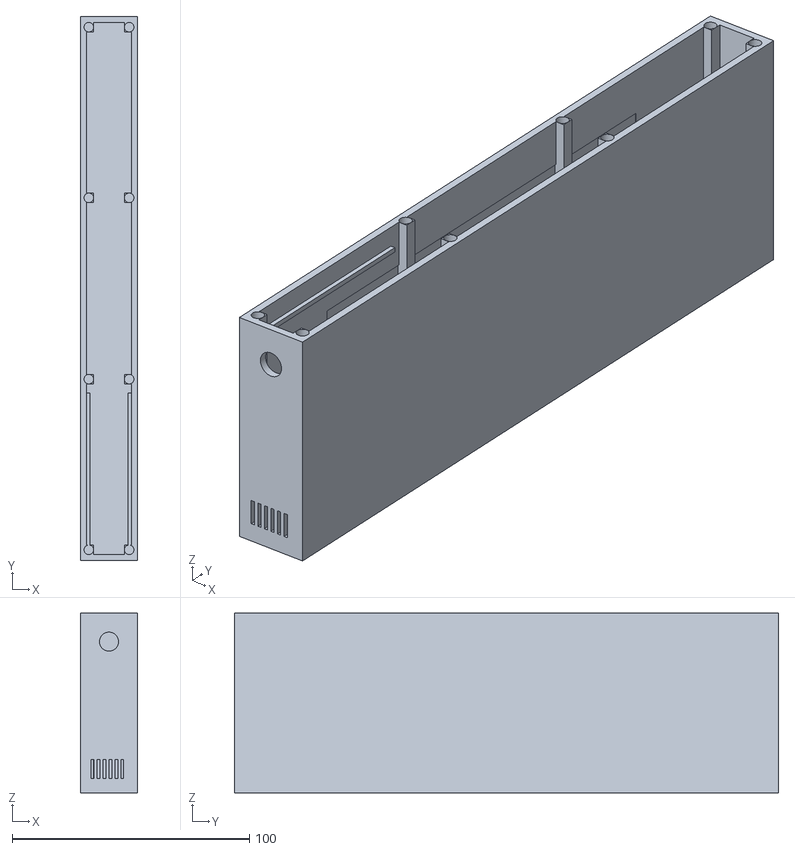
[picture p164: CAD file, 2026-09-05]
v2/release/revA/module/battery-module-base.stl
24.0 x 229.2 x 75.7
