meshsat/meshsat-fieldkit/compact/v2/coupons/meshsat-coupon_board.stl

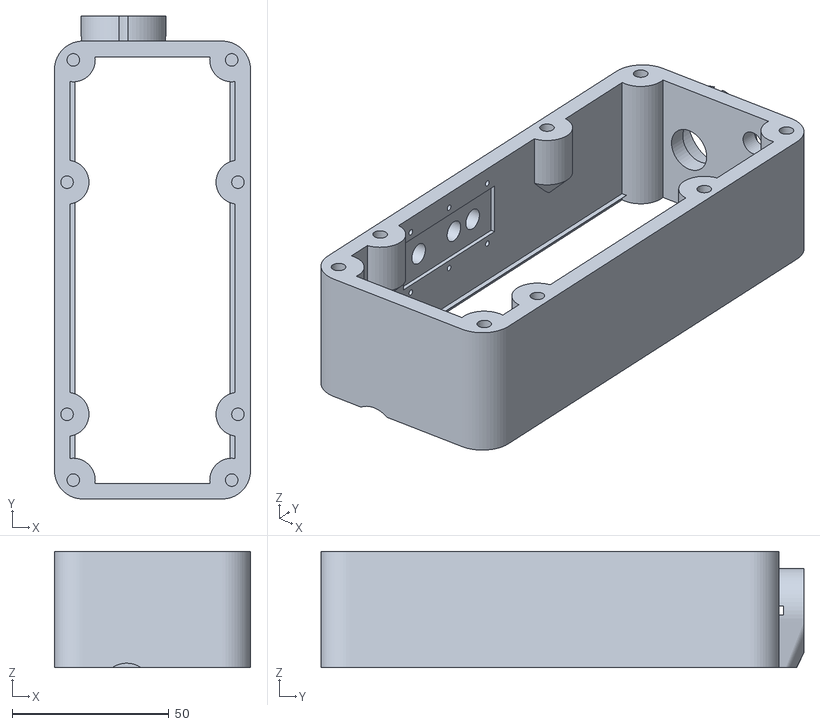
[picture p165: CAD file, 2026-10-06]
compact/v2/coupons/meshsat-coupon_board.stl
62.5 x 154.0 x 37.0
