meshsat/meshsat-fieldkit/compact/v2/reference-cad/groundcontrol-rockblock-9704/Mount_for_RockBLOCK_9704-SMA_RevA.STEP

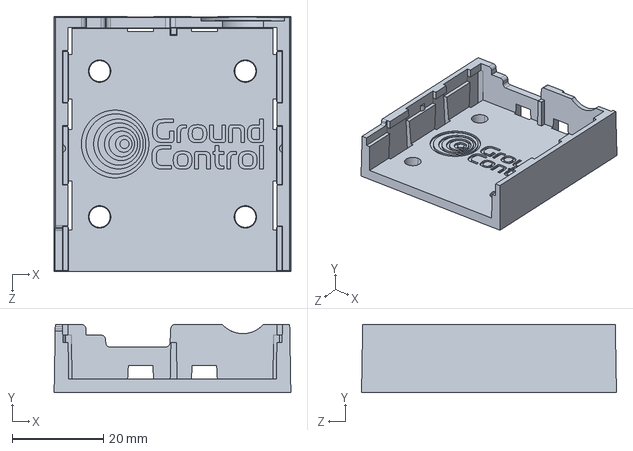
[picture p166: CAD file, 2026-10-06]
compact/v2/reference-cad/groundcontrol-rockblock-9704/Mount_for_RockBLOCK_9704-SMA_RevA.STEP
52.0 x 15.0 x 56.0 mm
