meshsat/meshsat-fieldkit/compact/v2/reference-cad/lilygo-t-beam-supreme/lilygo-shell/brackets.stl

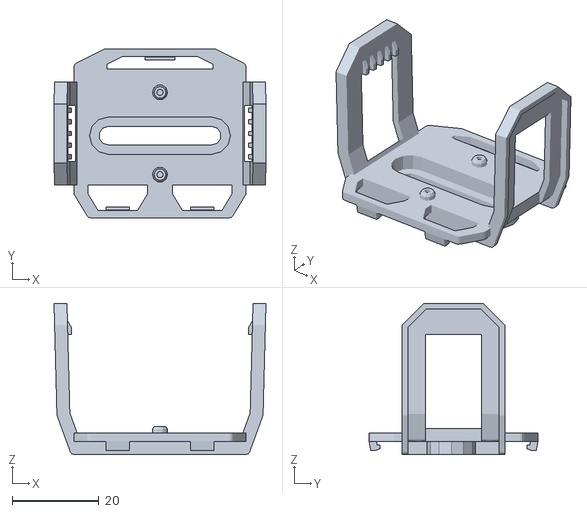
[picture p167: CAD file, 2026-10-06]
compact/v2/reference-cad/lilygo-t-beam-supreme/lilygo-shell/brackets.stl
49.0 x 39.0 x 35.0
