meshsat/meshsat-fieldkit/compact/v2/reference-cad/lilygo-t-beam-supreme/T-BEAM-SUPREME-V3.0.DXF

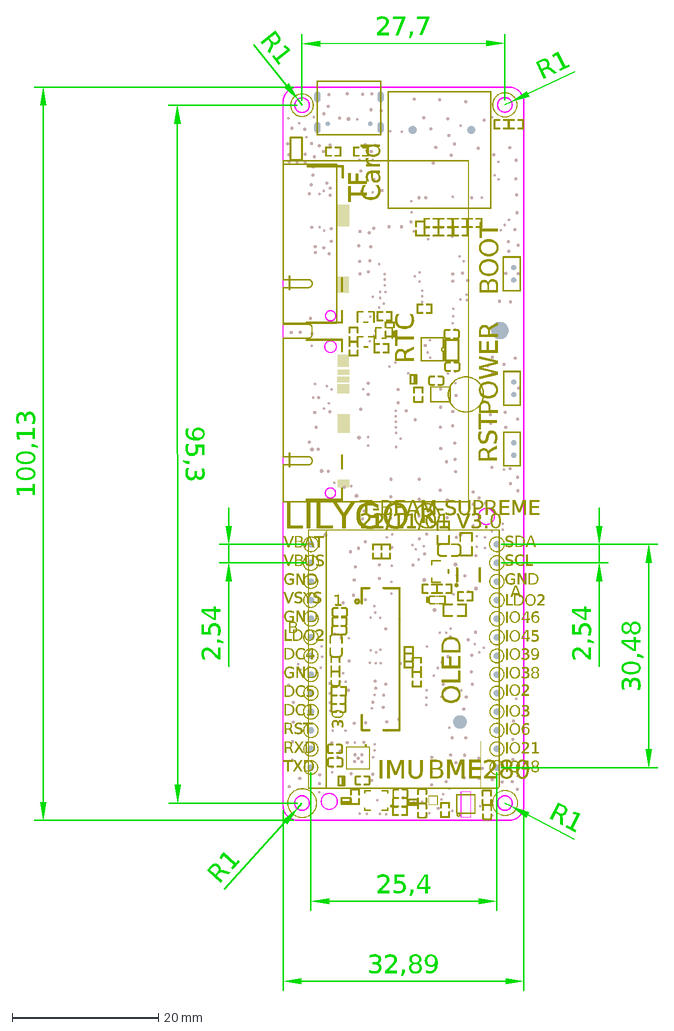
[picture p168: CAD file, 2026-10-06]
compact/v2/reference-cad/lilygo-t-beam-supreme/T-BEAM-SUPREME-V3.0.DXF
22/11/01 V3.0
T-BEAM-SUPREME
POWER
RST
BOOT
VBAT
VBUS
GND
VSYS
LDO2
DC4
DC5
DC1
RXD
TXD
SDA
SCL
IO46
IO45
IO39
IO38
IO2
IO3
IO6
IO48
A
B
IO21
LILYGO®
RTC
OLED
IMU
BME280
Card
TF
1
30
27,7
95,3
32,89
100,13
2,54
R1
25,4
30,48
