meshsat/meshsat-fieldkit/compact/v2/reference-cad/meshes/rb9704_step.stl

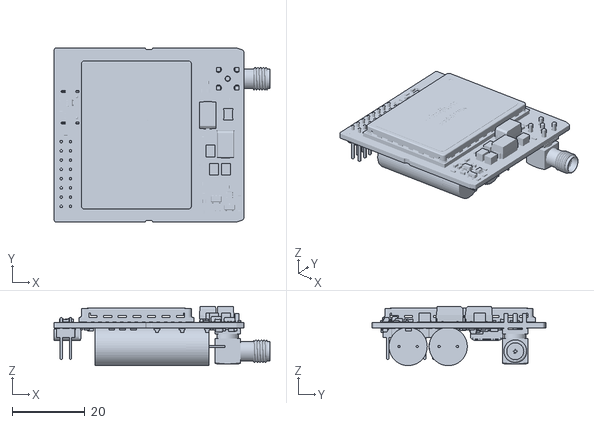
[picture p169: CAD file, 2026-10-06]
compact/v2/reference-cad/meshes/rb9704_step.stl
59.3 x 47.8 x 16.2
