meshsat/meshsat-fieldkit/compact/v2/validation/build/body.stl

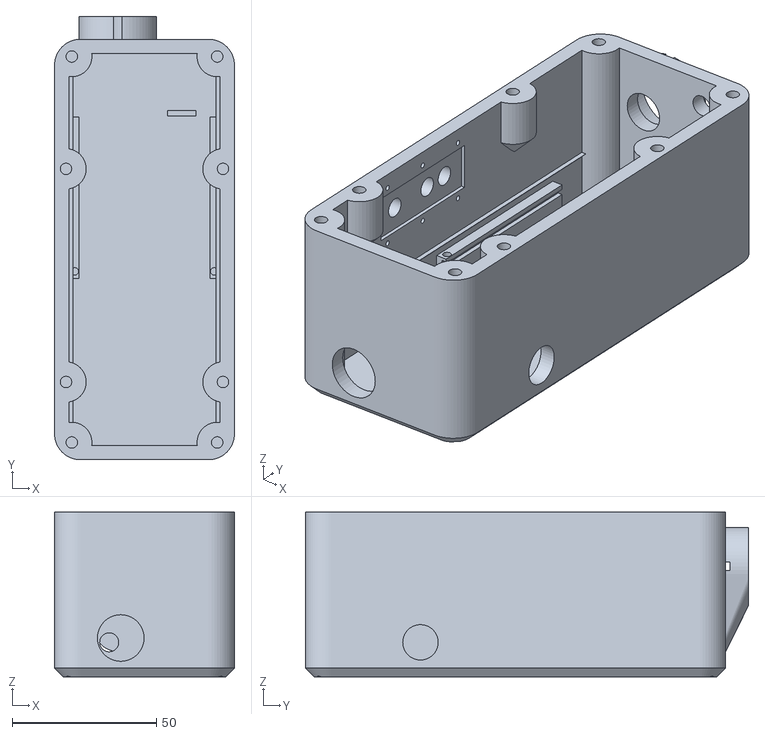
[picture p170: CAD file, 2026-10-06]
compact/v2/validation/build/body.stl
62.5 x 154.0 x 57.2
