meshsat/meshsat-fieldkit/v2/cad/render/stl/epaper.stl

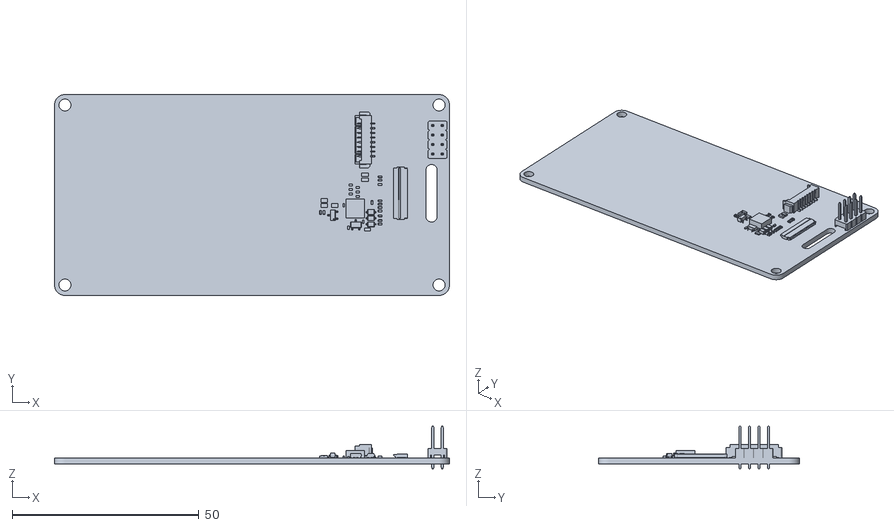
[picture p171: CAD file, 2026-09-05]
v2/cad/render/stl/epaper.stl
105.8 x 53.8 x 11.5
