meshsat/meshsat-fieldkit/v2/docs/records/a1mech/cad/lid-pack-a1-B-module.step

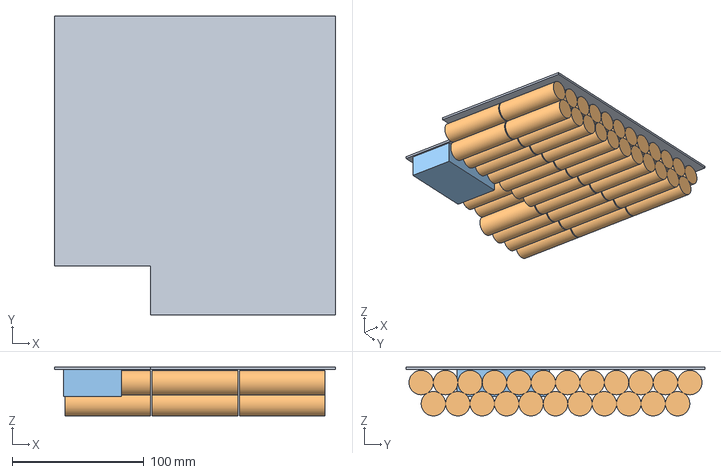
[picture p172: CAD file, 2026-09-29]
v2/docs/records/a1mech/cad/lid-pack-a1-B-module.step
213.8 x 227.1 x 37.1 mm
