meshsat/meshsat-fieldkit/v2/release/case-2026-09-27/connector-plate/connector-plate.step

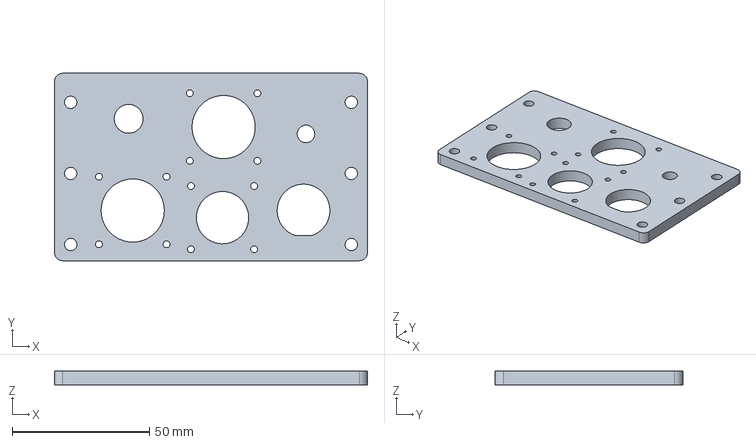
[picture p173: CAD file, 2026-09-27]
v2/release/case-2026-09-27/connector-plate/connector-plate.step
114.0 x 68.3 x 5.00 mm
