meshsat/meshsat-fieldkit/v2/release/case-2026-09-27/frame-legs/frame-leg.step

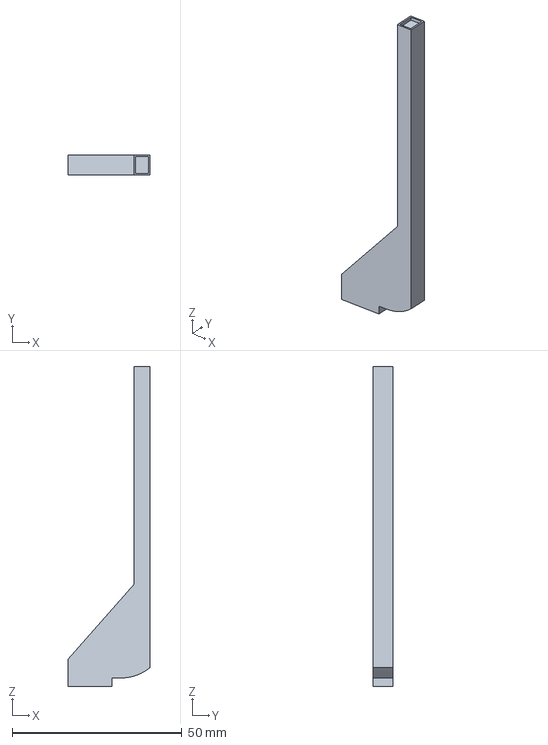
[picture p174: CAD file, 2026-09-27]
v2/release/case-2026-09-27/frame-legs/frame-leg.step
24.2 x 6.00 x 94.1 mm
