meshsat/meshsat-fieldkit/v2/release/case-2026-09-27/lid-tray-qmx-r2/lid-plate-qmx-r2.step

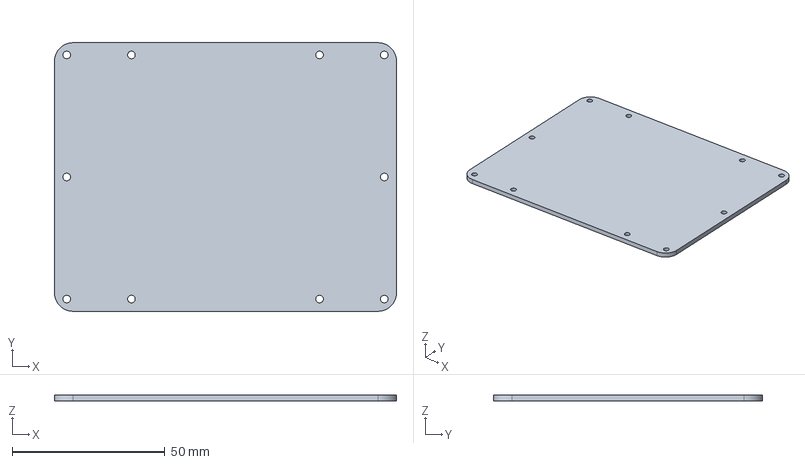
[picture p175: CAD file, 2026-09-28]
v2/release/case-2026-09-27/lid-tray-qmx-r2/lid-plate-qmx-r2.step
111.8 x 87.8 x 2.00 mm
