meshsat/meshsat-fieldkit/v2/release/handover/H1/v2/release/revA/module/battery-module-cradle.step

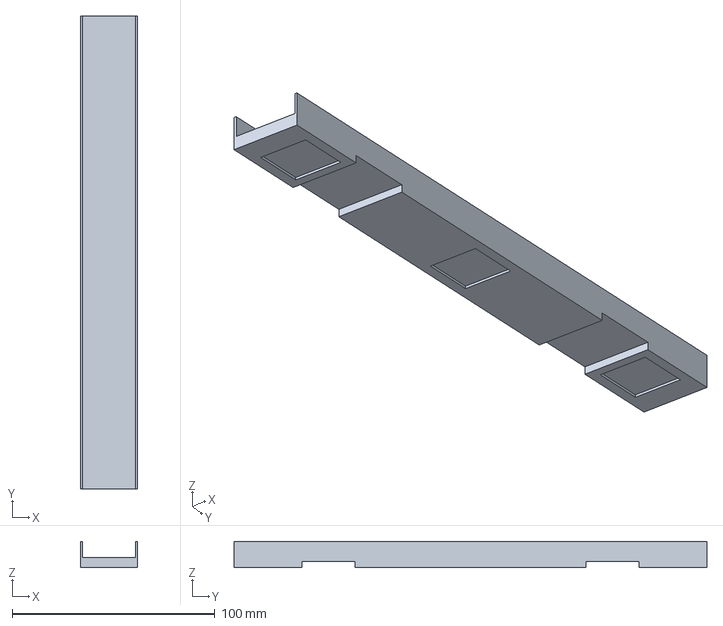
[picture p177: CAD file, 2026-09-05]
v2/release/handover/H1/v2/release/revA/module/battery-module-cradle.step
28.0 x 233.2 x 13.0 mm
