meshsat/meshsat-fieldkit/compact/v2/coupons/meshsat-coupon_rimlid.stl

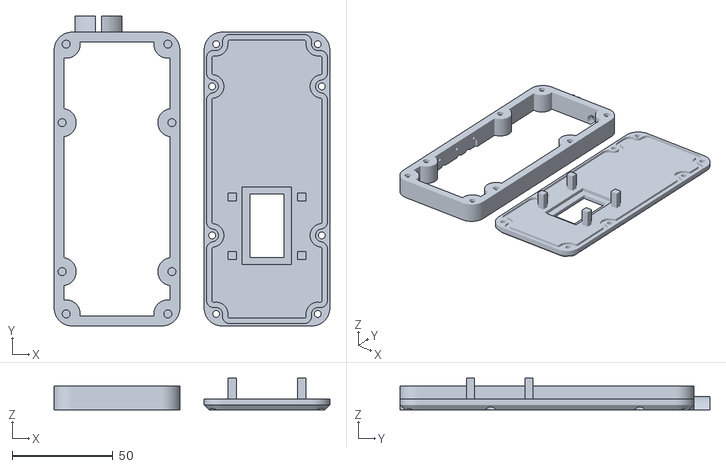
[picture p178: CAD file, 2026-10-06]
compact/v2/coupons/meshsat-coupon_rimlid.stl
137.0 x 154.0 x 15.8
