meshsat/meshsat-fieldkit/compact/v2/print-stl/meshsat-belt.stl

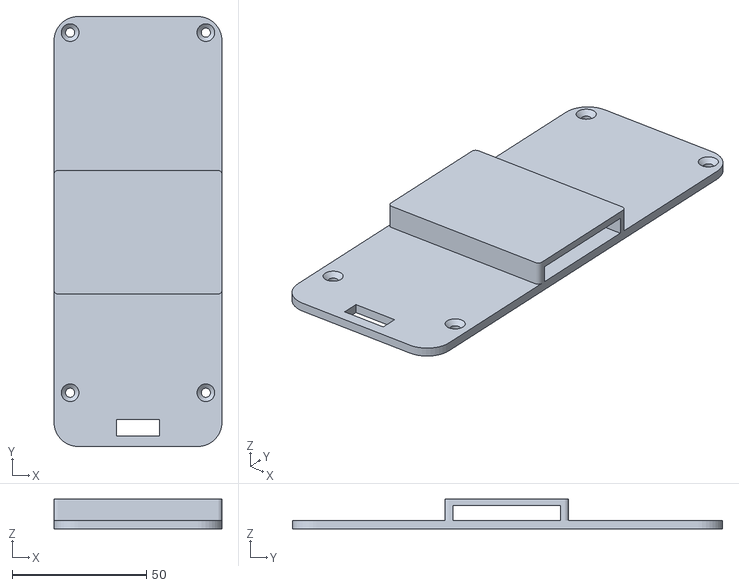
[picture p179: CAD file, 2026-10-06]
compact/v2/print-stl/meshsat-belt.stl
62.5 x 160.0 x 11.0
