meshsat/meshsat-fieldkit/compact/v2/reference-cad/lilygo-t-beam-supreme/lilygo-shell/topside.stl

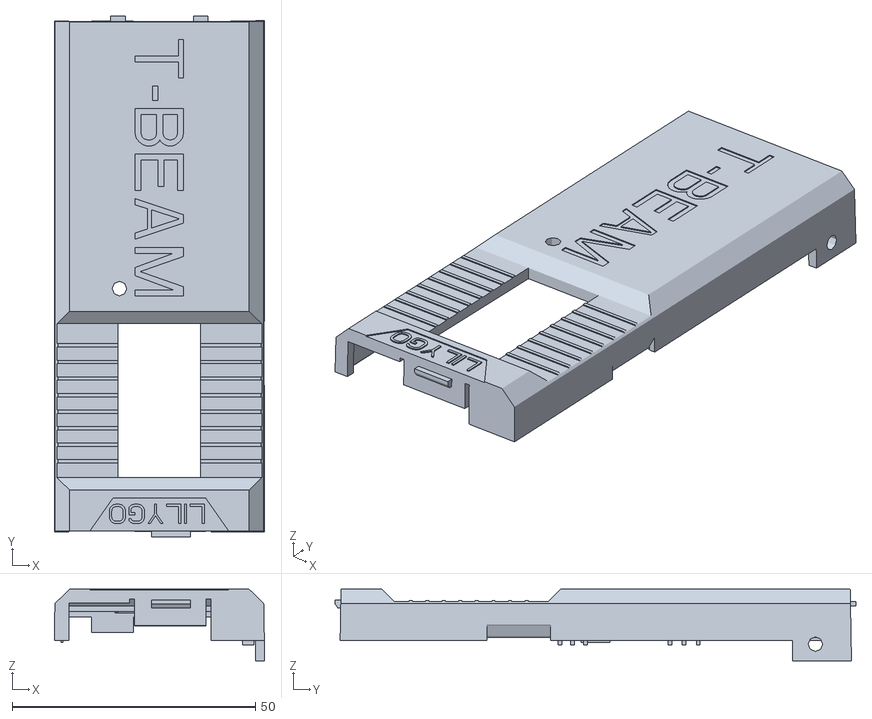
[picture p180: CAD file, 2026-10-06]
compact/v2/reference-cad/lilygo-t-beam-supreme/lilygo-shell/topside.stl
43.3 x 107.1 x 14.7
