meshsat/meshsat-fieldkit/compact/v2/validation/build/a_plungers.stl

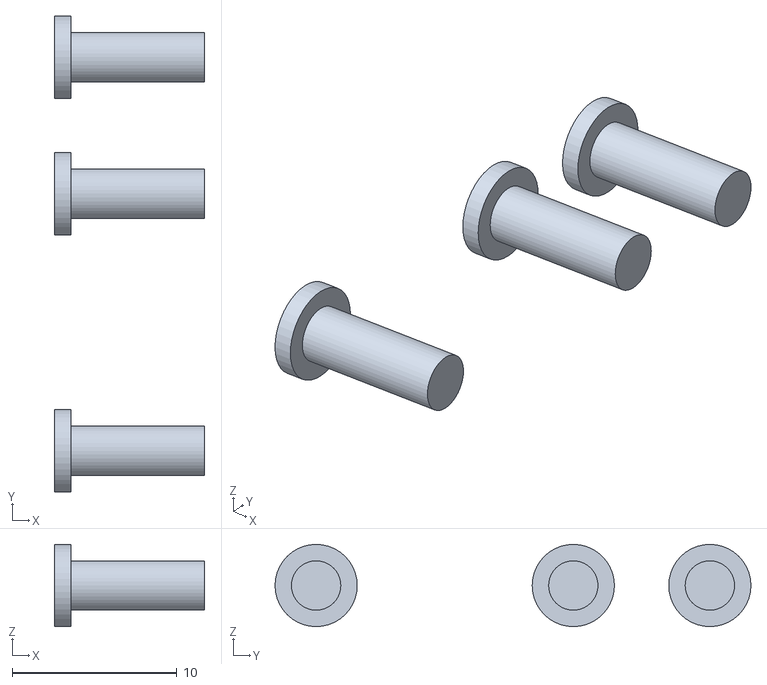
[picture p181: CAD file, 2026-10-06]
compact/v2/validation/build/a_plungers.stl
9.13 x 28.9 x 5.00
