meshsat/meshsat-fieldkit/v2/cad/render/stl/module_base.stl

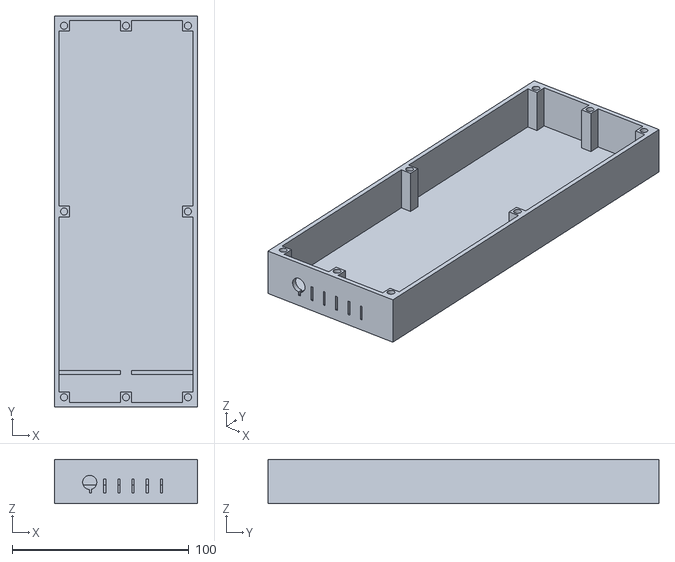
[picture p182: CAD file, 2026-09-05]
v2/cad/render/stl/module_base.stl
81.0 x 221.0 x 25.0
