meshsat/meshsat-fieldkit/v2/release/case-2026-09-27/frame-legs/wedge.step

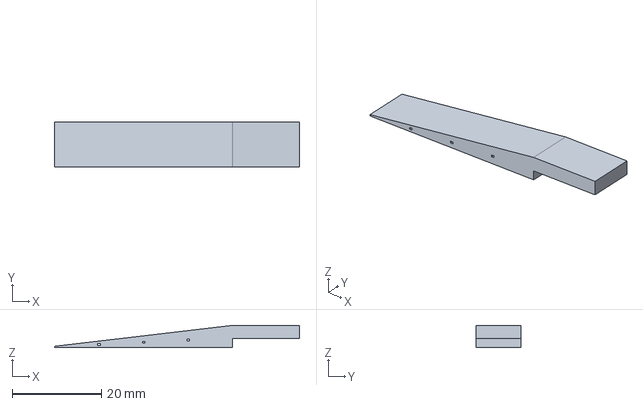
[picture p183: CAD file, 2026-09-27]
v2/release/case-2026-09-27/frame-legs/wedge.step
55.0 x 10.0 x 5.00 mm
