meshsat/meshsat-fieldkit/v2/release/case-2026-09-27/rf-entry-plates/rf-entry-plate-west.step

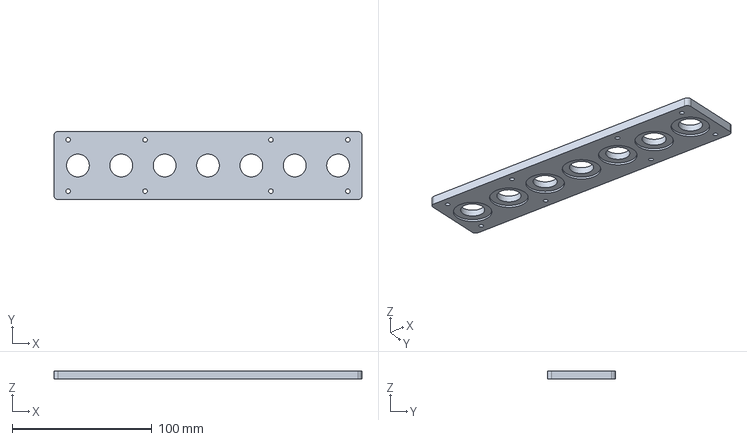
[picture p185: CAD file, 2026-09-27]
v2/release/case-2026-09-27/rf-entry-plates/rf-entry-plate-west.step
220.2 x 48.9 x 6.00 mm
