meshsat/meshsat-fieldkit/compact/v2/print-stl/meshsat-molle.stl

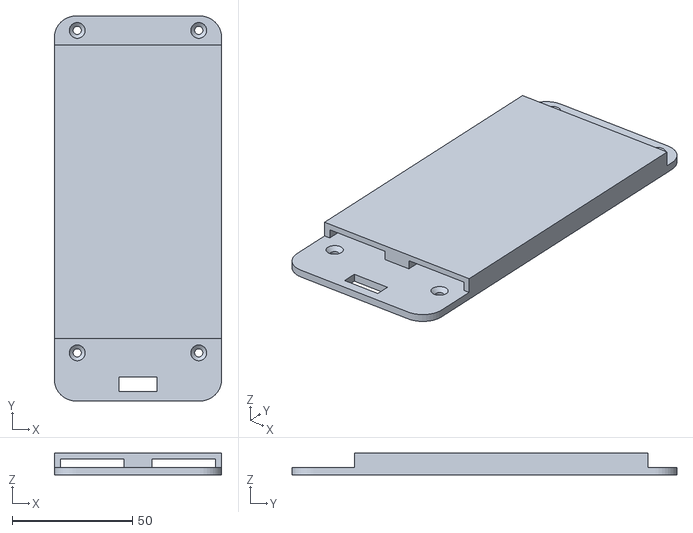
[picture p186: CAD file, 2026-10-06]
compact/v2/print-stl/meshsat-molle.stl
69.6 x 160.0 x 9.00
