meshsat/meshsat-fieldkit/compact/v2/validation/build/chk_rail_lip.stl

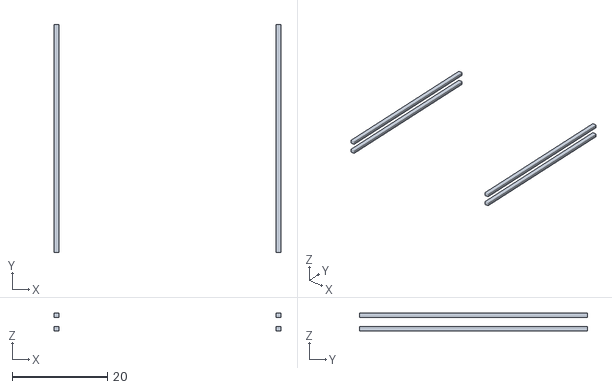
[picture p187: CAD file, 2026-10-06]
compact/v2/validation/build/chk_rail_lip.stl
47.7 x 48.0 x 3.75
