meshsat/meshsat-fieldkit/v2/cad/render/stl/panel_frame.stl

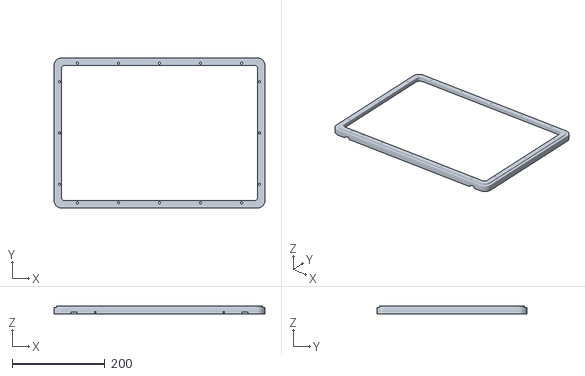
[picture p188: CAD file, 2026-09-05]
v2/cad/render/stl/panel_frame.stl
455.2 x 323.9 x 18.0
