meshsat/meshsat-fieldkit/v2/release/case-2026-09-27/frame-legs/leg-locator.step

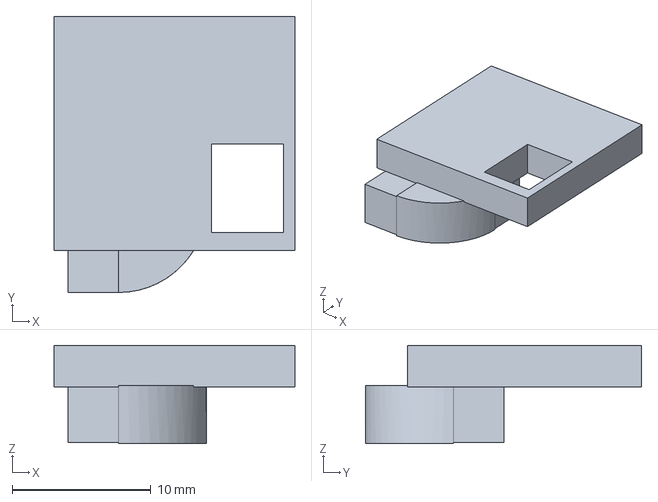
[picture p189: CAD file, 2026-09-27]
v2/release/case-2026-09-27/frame-legs/leg-locator.step
17.4 x 19.9 x 7.10 mm
