meshsat/meshsat-fieldkit/v2/release/handover/H1/v2/release/revA/module/float-nest-smp-max.step

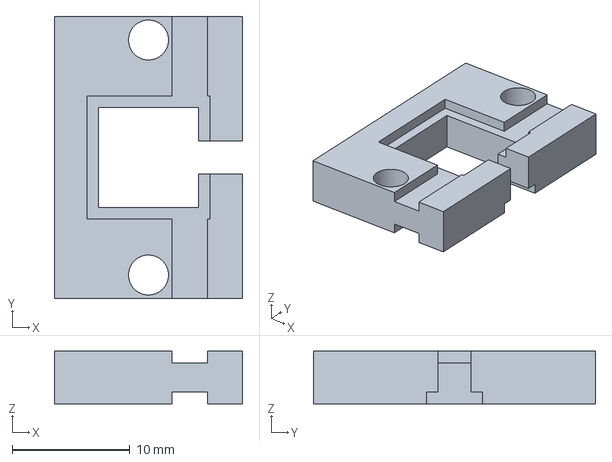
[picture p190: CAD file, 2026-09-04]
v2/release/handover/H1/v2/release/revA/module/float-nest-smp-max.step
16.0 x 24.0 x 4.50 mm
