meshsat/meshsat-fieldkit/compact/v2/print-stl/meshsat-retainer.stl

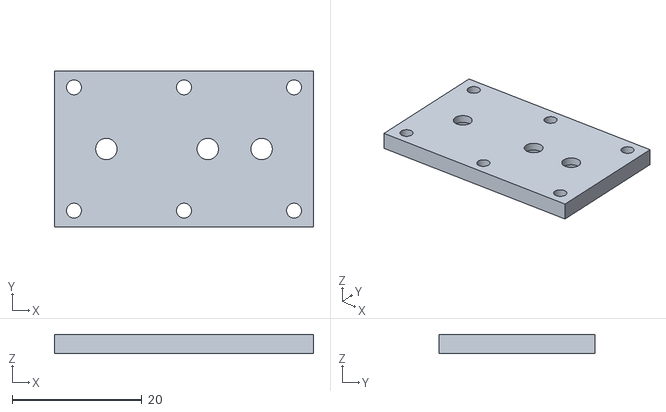
[picture p191: CAD file, 2026-10-06]
compact/v2/print-stl/meshsat-retainer.stl
39.9 x 24.0 x 3.00
