meshsat/meshsat-fieldkit/compact/v2/print-stl/meshsat-separator.stl

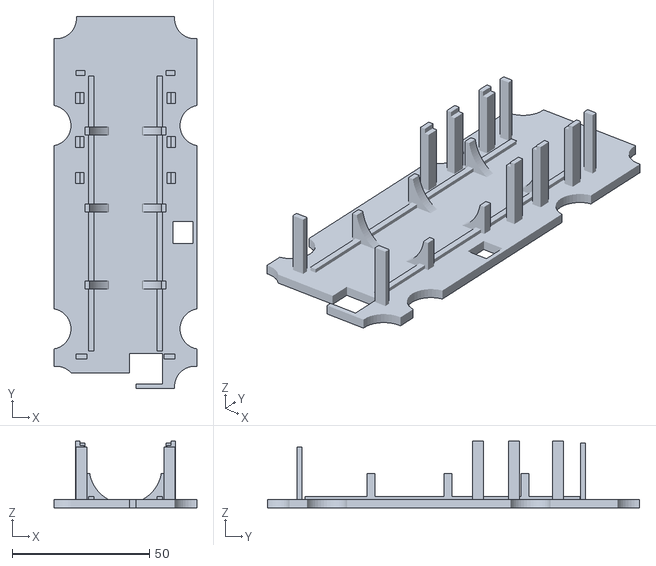
[picture p192: CAD file, 2026-10-06]
compact/v2/print-stl/meshsat-separator.stl
51.9 x 135.4 x 24.3
