meshsat/meshsat-fieldkit/compact/v2/validation/build/a_membrane.stl

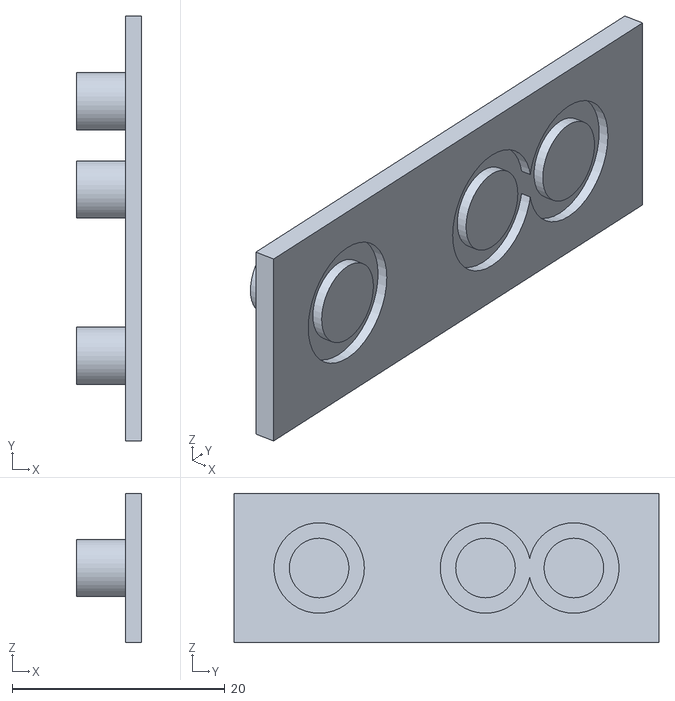
[picture p193: CAD file, 2026-10-06]
compact/v2/validation/build/a_membrane.stl
6.10 x 39.9 x 14.0
