meshsat/meshsat-fieldkit/v2/cad/render/stl/td2.stl

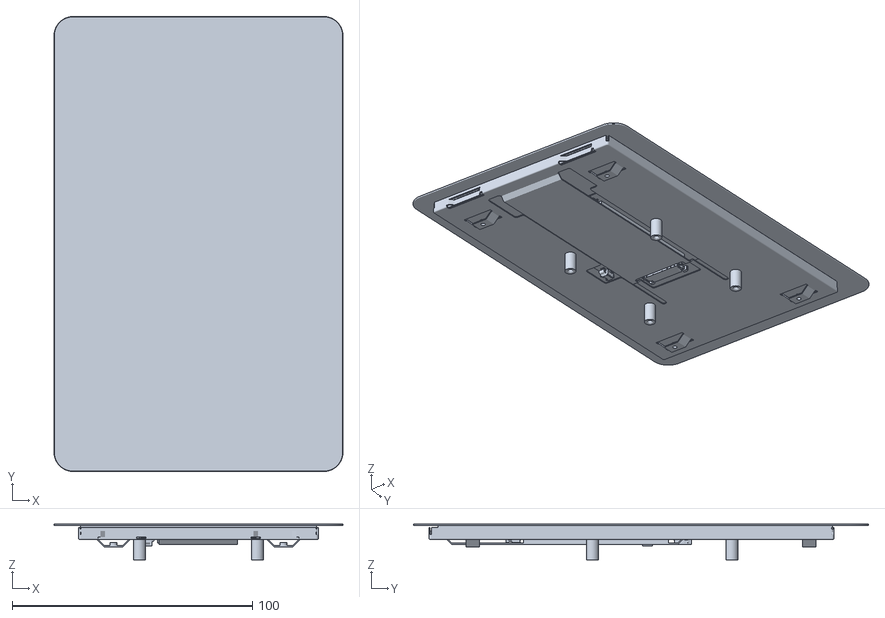
[picture p194: CAD file, 2026-09-05]
v2/cad/render/stl/td2.stl
120.2 x 189.3 x 15.0
