meshsat/meshsat-fieldkit/v2/cad/render/stl/module_cradle.stl

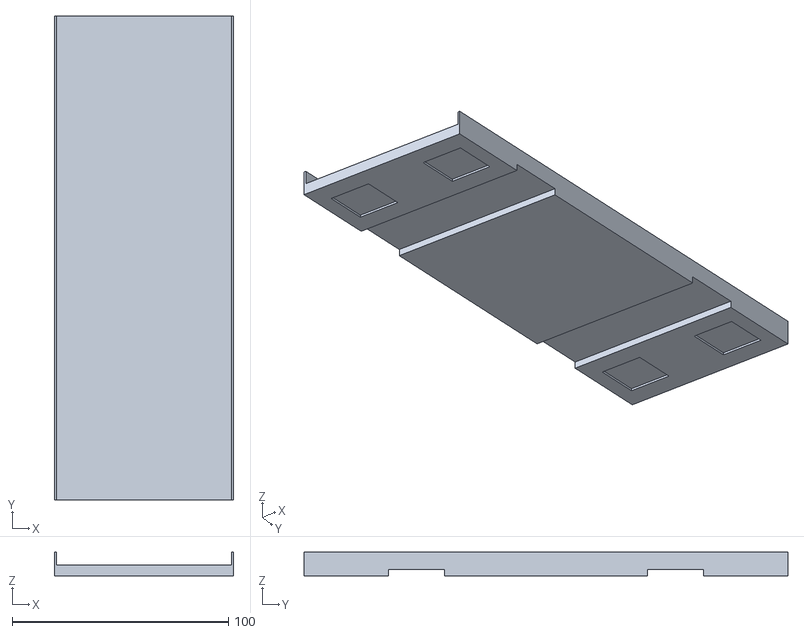
[picture p195: CAD file, 2026-09-04]
v2/cad/render/stl/module_cradle.stl
83.0 x 224.0 x 11.0
