meshsat/meshsat-fieldkit/20261010_Handover/02_Concept_of_Operations/v2/docs/reviews/REVIEW-A-LAYER-2-2026-09-27.md

# AI review (not a qualified engineering review): Review A, layer 2 (concept of operations), pass 2

MESHSAT-1357. Written 27 September 2026, about 06:50 CEST, by a fresh AI reviewer (a Claude subagent). This reviewer
wrote none of the layer's documents, did not hold the first pass and did not assemble the handover. This is an **AI
review**. It replaces none of the qualified reviews the records require (D-09: R-BAT, R-SEC and the others), and it
establishes no circuit's correctness. Prototype design: nothing has been built, ordered, powered or deployed.

This file overwrites the first pass's record at the same path, as the brief asks. The first pass (FAIL, seven blocking
findings B1 to B7, twelve minor m1 to m12) is preserved verbatim outside the worktree at
`scratchpad/rvA2/REVIEW-A-LAYER-2-2026-09-27.pass1.md` (sha256 `e854c2a46ea3d542...`) for the records integrator to
file beside this one; section 3 below lists each of its findings with the answer this pass checked.

## 1. What was read

**Worktree:** `scratchpad/wt/hc2`, branch `fnd/hc2`.
- `git rev-parse HEAD` = `e3aedb25c849dbda931888b27093ac6c444621cb`, with uncommitted changes.
- `git diff --stat`: 5 files changed, 1000 insertions and 193 deletions: `v2/docs/CONOPS.md` (758),
  `v2/docs/OPERATING-ENVELOPE.md` (174), `v2/docs/PANEL.md` (8), `v2/docs/TEST-PLAN.md` (180),
  `v2/ecad/tools/pcb_envelope.yaml` (73).
- Untracked: `drafts/` and this record.

This is not a pinned commit. The baseline commit must carry the sha256 values below for the five files, or the
difference must be reviewed.

**Files judged** (sha256, first 16 hex digits; they equal `drafts/final-shas.txt`):

| sha256/16 | File |
|---|---|
| ab28e85bebec4e4c | `v2/docs/CONOPS.md` |
| 6930e4f05a59ac5c | `v2/docs/OPERATING-ENVELOPE.md` |
| 6333e5d212f57a78 | `v2/ecad/tools/pcb_envelope.yaml` |
| 5bffe28fcca3283f | `v2/docs/PANEL.md` (section 9 changed) |
| a87e66cf431d938d | `v2/docs/TEST-PLAN.md` |
| 5790bc7e444bebc4 / 835910e807d588c4 | `drafts/pwr_red2.py` / `drafts/pwr_red2.out` (to be filed as `records/hc2/`) |
| 932fec2a1ae394e6 | `drafts/handoffs.md` |
| 274d4eee84971521 | `drafts/sc.md` |
| 2ae6c38edd55f051 | `drafts/LAYER-STATUS-layer2.md` |
| fa2b60fbf4cdc486 | `drafts/gen_sch_b.BANK-R1.patch` |
| 8ac3c352b99853cd | `drafts/ASSEMBLY.step10-and-lamp-test.patch` |
| 3f384a558f02729c | `drafts/part_temps.patch` |
| dbc256931885af15 | `drafts/REVIEW-A-BRIEF.md` |

**Sources checked against, at `e3aedb25`:**

| sha256/16 | Source |
|---|---|
| 6c3c93b7f32f953a | `v2/docs/ARCH-PCB-B-IOHA.md` (sections 2, 4 to 8, 10, 12, 13, 15, 15a) |
| bb9c861c9920c8d6 | `v2/docs/feasibility/POWER-THERMAL.md` (7.1, 9.3, 9.4) |
| e57a54d1767bcd59 | `v2/docs/feasibility/EMCON.md` (4.5, 5a) |
| 7f6c34697753bac1 | `v2/ecad/tools/gen_sch_a.py` (the charger at 0x6B, line 708; R17 the 5 mOhm RSR shunt, lines 24 to 48) |
| dedaf34ce285e5ff | `v2/ecad/tools/gen_sch_b.py` (`PORTS` lines 764 to 766; the ring `f = s % 3 + 1` line 788; CP2102N supplies lines 919, 937, 949; `U19` line 974; `U6` on the kit bus lines 1030 to 1040) |
| 5f1ce2dd66ed7d2d | `v2/ecad/tools/gen_sch_c.py` (LEDs lines 190 to 206) |
| d120ebfb9afbee6e | `v2/ecad/tools/gen_sch_e.py` (lines 213, 503 to 508, 524 to 542) |
| 28904a37f2f18103 | `v2/ecad/tools/check_pcb_b.py` (the BEARERS invariant, lines 424 to 431) |
| 469d0820b046ef6f | `v2/docs/records/rv-pwr/pwr_budget.py` |
| 2bae882148b45172 | `v2/vendor/quectel/quectel-rm520n-series-hardware-design-v1.1.pdf` (section 3.2, the feature table) |
| 3e5e927fdf63cf6a | `v2/vendor/ti/bq25731-datasheet.pdf` (SLUSE66A 9.6.8, 9.6.10, Table 9-8) |
| 331f35ed1f027a74 | `v2/vendor/sensirion/sgp41-datasheet.pdf` (operating -20 to +55 C) |
| 5e942dd41e9e4ed0 | `v2/docs/MESHSAT-709-geometry-appendix.md` (32.50 item 6, 32.53 line 2860) |
| acd19f7bfc50b7ad | `v2/ecad/tools/pcb_requirements.yaml` (REQ-025, REQ-036, REQ-052 as they stand) |

**Main as it stands now:** `84e52461` (not `53a98a71`, which `drafts/handoffs.md` section 1 is written against),
compared for integration only: `pcb_requirements.yaml` 00029b87049b1f5f, `PANEL.md` 8eeb152e4d82080c, `ASSEMBLY.md`
30db27eee509212c, `pcb_pack_protection.yaml` 54039554131c1e26, `gen_sch_d.py` 0f1d59fd60ffb5ef,
`review-packets/battery/THERMAL-COORDINATION.md` (its section 4 tables).

**Run:** `drafts/pwr_red2.py`, copied with `pwr_budget.py` at `e3aedb25` into this reviewer's own scratch directory
(outside the worktree and the main tree), reproduces `drafts/pwr_red2.out` byte for byte (sha256 `835910e807d588c4...`,
under a second). **Not re-run:** the closer's `rules_lib.py`, `rules_render.py` and test results, because they write
into a tree. Nothing was run in the main tree, and nothing in the worktree was edited except this record.

## 2. What was verified and holds

- **The bank facts behind every mode.** CONOPS 4c (lines 477 to 488) matches `ARCH-PCB-B-IOHA.md` sections 4 and 15
  and the generator: bank s fails over to slot `s % 3 + 1`; each module has two host ports (USB3-0 home, USB3-1 one
  neighbour bank), so slot 2 can host banks 2 and 1 and slot 3 banks 3 and 2 at once; the four CP2102N bridges are on
  `+5V_DEV` and the radios' software enables are on the kit-bus expander `U6`, so no bank device depends on a dropped
  slot's rail. The per-slot tables (what slot 1, 2 or 3 alone carries) are right.
- **BANK-R1.** The patch exchanges exactly `RB_DP/DM` with `QMX_DP/DM` (port 4, banks 1 and 2) and `USB_PNL_P/N` with
  `USB_WALL_P/N` (bank 1 port 2, bank 3 port 3). On the result, `check_pcb_b.py`'s BEARERS invariant (Iridium, HF,
  APRS) has one bearer per bank; slot 3 alone then hosts GNSS, both E72, Iridium, APRS, the sensor controller, the
  panel controller and LoRa; three of the four core bearers survive any one module loss, as CONOPS line 579 says.
- **B1's sources.** Quectel HD v1.1 section 3.2: in both PCIe modes the module "Supports MBIM/QMI/QRTR/AT over PCIe
  interface", and "For USB-AT-based PCIe mode, the firmware upgrade via PCIe interface is not supported, so USB 2.0
  interface must be reserved for the firmware upgrade". SLUSE66A: VBAT 64 mV per LSB for 1S to 4S (9.6.10); IDCHG
  512 mA per LSB with a 5 mOhm RSR (9.6.8); EN_LWPWR resets to 1 and "ADC is not available in Low Power Mode" (Table
  9-8). `gen_sch_a.py` line 708: the BQ25731 at 0x6B on the kit bus; R17 is the 5 mOhm shunt. 12.8 V less one cell at
  2.50 V leaves 3.43 V on each of the others, as line 723 says.
- **B2's source.** `gen_sch_e.py` lines 524 to 542: the reed reaches the sensor controller alone. The start-up cost
  (60.6 W over two minutes, 7.3 kJ, into 8 to 10 kJ/K, appendix 32.53 line 2860) is under 1 K.
- **B3's arithmetic.** About 108 Wh usable when aged (42.8 x 2.5, 31.38 x 3.47, 21.73 x 5.03); 21.7 W for 7 h is
  about 152 Wh; the daily solar hours (10 to 11, 7.5 to 8, 5 to 5.5) follow from 100 W of front end.
- **Every new figure of pass 2** (PS-SURV-R 23.3 W, 12.8 to 46.9, 5.9 / 4.7 / 3.5 h; PS-EMCON aged 60 % 1.7 h; the
  stage-ambient rows of CONOPS 4c lines 612 to 618; the hot-end cell corners of lines 631 to 636; the COLD block
  rows of lines 661 to 666; 72.7 W over 20 K = 3.6 W/K; `pcb_envelope.yaml`'s `inside_air_bounds_k`,
  `worst_inside_air_c` and `cold_end`; OPERATING-ENVELOPE section 3's tables and the +61.6 to +74.2 C at +55 C)
  reproduces from `pwr_red2.out`.
- **The lamp test.** `gen_sch_c.py`: fifteen expander LEDs plus the TX lamp `D3` make `D1` to `D16`; with the PI ring
  that is seventeen controller-lit indicators, as PANEL line 184, CONOPS line 998 and the ASSEMBLY patch now say.
- **TEST-PLAN.** E3-L carries E3-A's pass line with the lid closed, the owner's example with the SOS path at every
  level, the SGP41 as a failure, and does not waive the generated board; E4-O restores UTC +1.0 C and UTD -9.0 C and
  requires the link after the warm-up; T-H3 replaces ASSEMBLY step 10; the stored and transport states have every
  input unplugged.
- **Labelling elsewhere.** Every 7a row, the Reduced and Heat stage rows, OPERATING-ENVELOPE section 8's D-02b
  paragraph ("The session's definition of 27 September 2026"), `pcb_envelope.yaml`'s `hot_end` and `session_taken`, and
  TEST-PLAN section 1 ("session text, not an owner ruling") mark the session's choices. No em dash was added. Nothing
  is claimed built, tested or working.

## 3. The first pass's findings, each answer checked

| Finding | Answer checked | Disposition |
|---|---|---|
| B1 heat stage losses, 5G, shutdown source | CONOPS line 308, 536 to 557, 715 to 726; 4f line 802; SC-L2-02, 10 | answered (n4 and n8 below are precision items) |
| B2 lid-closed start-up | Startup row line 305, 4c lines 513 to 524, SC-L2-17 | answered |
| B3 M1 and the night | M1 lines 175 to 198, section 6, D-06 row, SC-L2-05 | answered (n11: no decision point) |
| B4 E3-L pass line | TEST-PLAN line 135 | answered |
| B5 REQ-052 not restated down | 4c lines 526 to 591, handoffs 3.6, SC-L2-18, BANK-R1 patch | answered (n1: BANK-R1's cost to the SGP41 unstated) |
| B6 ASSEMBLY step 10 | 4d step 1, T-H3, ASSEMBLY patch | answered (the patch lands with its owner) |
| B7 the cold end | 4c lines 648 to 695, OE section 4, `cold_end`, E4-O | answered (n3 and n10) |
| m1 to m10, m12 | as the brief's table maps them | answered; m4's wording is what P2-B2 below finds incomplete |
| m11 records not filed | handoffs 1 and 12 | still open until the integrating commit (n14) |

## 4. Findings of this pass
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
