meshsat/meshsat-fieldkit/20261010_Handover/03_Requirements/v2/docs/handover/layer3/OWNER-INSTRUCTION-2026-09-30.md

# The owner's instructions of 30 September 2026: finish layer 3 for the current target, and his review of the draft table

## Current owner brief (read this first; kept under D-31)

The one authoritative interpretation both agents read first (D-30, D-31); each line names the ruling that carries it,
quoted below and recorded in `v2/ecad/tools/pcb_requirements.yaml` (`owner_rulings`). Recommendations and earlier model
statements are not owner approval (D-31).

**Constraints.** (1) Battery storage inside the Peli 1450; NO external battery (D-28; row L3-OD7, D-32; REQ-014).
(2) Battery and solar required (D-20, D-21, D-28; REQ-014, REQ-016). (3) HF and the tablet functions kept, the QMX set
and the tablet bracket in the lid (D-28; row L3-OD2, D-33; REQ-002, REQ-011). (4) 48 to 72 hours is a baseline design
objective under a stated operating profile, not a mandatory minimum (D-28; D-32; REQ-072, the only design objective).
(5) Optional tablet charging consumes the kit's energy and reduces endurance, below the target included; no daily
schedule is mandatory, the 36 Wh a day illustrative (D-28; REQ-011). (6) Every other explicitly approved requirement
unchanged, REQ-016's solar window among them (D-28; row L3-OD3, D-34); a proposed change to approved operating
conditions stays an owner decision (D-31).
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
