meshsat/meshsat-fieldkit/compact/v2/renders/renders_assembly.png

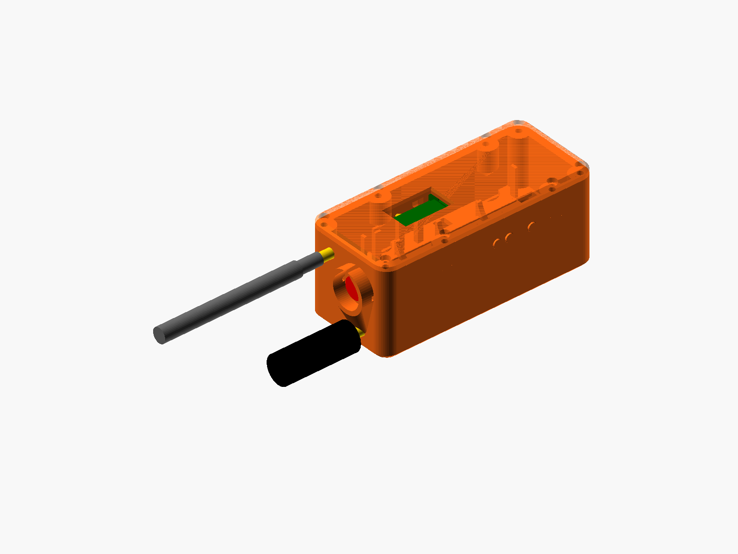
compact/v2/renders/renders_assembly.png
