meshsat/meshsat-fieldkit/v2/docs/test-procedures/TP-E11-37.md

# TP-E11-37: BATDRV with the three battery FETs (supplement entry, ideal diode, LDO mode, current sharing)

<!-- tp
id: TP-E11-37
title: BATDRV with the three battery FETs (supplement entry, ideal diode, LDO mode, current sharing)
register: R-183
e11: E11-37
route5d: E11-37 (R-183)
-->

**Status: PROPOSED, for the supplier to review and agree before execution.** MESHSAT-1357, 3 October 2026; re-read on 4 October
2026 against L4-E11's round 9 and L4-E9's rows for set 29. Prototype design: nothing here has been built, bought, powered or
measured. Common rules: `v2/docs/test-procedures/README.md`.

## 1. Purpose and the decision it settles

TI asks for a battery FET whose Ciss is under 5 nF and does not say what the 5 nF bounds. One BUK6Y10-30P is under that figure on
typical data; the three that L4-E11's round 9 drafts in parallel on one BATDRV (Q39, Q40 and Q42) are over it. The record, for one
part:

<!-- q src="v2/docs/records/l4e11/L4E11-SOURCE-ONLY-AND-ENTRY.md" -->
> TI's rule (SLUSE65A p.92) is "the Ciss of P-channel MOSFET should be chosen less than 5 nF"; TI prints the drive, RBATDRV_ON at
> most 6 kOhm and RBATDRV_OFF at most 2.1 kOhm, not the requirement behind 5 nF. The BUK6Y10-30P prints Ciss as a typical only:
> **2.36 nF at -15 V** (Table 7), no maximum and no spread; its Fig. 12 (typical) reads about **2.87 nF at -0.1 V**, near the
> battery FET's working point (on, or an ideal diode at 30 mV).
<!-- /q -->

Round 9 rebinds the row to the three:

<!-- q src="v2/docs/records/l4e11/L4E11-SOURCE-ONLY-AND-ENTRY.md" -->
> The owner's reviewer read E11-37 as covering the pair only, with transfer restricted to that gate network. It is rebound to the
> three:
>
> | Item | The pair | The three |
> |---|---|---|
> | Ciss at -15 V (typical, no maximum printed) | 4.72 nF | **7.08 nF**, 1.42 times TI's 5 nF (SLUSE65A p.92) |
> | Ciss near 0 V (Fig. 12, typical) | about 5.74 nF | **about 8.61 nF**, 1.72 times |
> | BATDRV on (6 kOhm at most), -15 V / near 0 V | 28.32 / 34.44 us | 42.48 / 51.66 us |
> | BATDRV off (2.1 kOhm at most), near 0 V | 12.05 us | 18.08 us |
>
> The bench now reads, besides the gate: **current sharing** (one gate node driving three thresholds, each drain's current in LDO
> mode and as an ideal diode) and **thermal coupling** (each junction on the shared pour). A result with the pair does not
> transfer to the three. **Q-TI-17** is extended to three devices (`clarification/TI-QUESTIONS.md`, drafted, not sent). **Thermal
> improvement alone cannot close the gate-drive question: E11-37 stays OPEN**, condition: Q-TI-17's answer or E11-37's bench with
> the three; production conformance needs one of them (record l9stk's C3).
<!-- /q -->

The decision, as the route table states it:

<!-- q src="v2/docs/records/l4e9/L4-POWER-ARCHITECTURE.md" row="E11-37 (R-183)" col="The decision it resolves" -->
> D-14's gate drive with the three FETs on one BATDRV (L4-E11 19d): Ciss 7.08 nF typical at -15 V and about 8.61 nF near 0 V
> against TI's 5 nF, each FET's current share and junction; OPEN on Q-TI-17 or this bench: the three (S1), or on a negative answer
> the pair at its fallback or one FET with a heat path through the case (S2)
<!-- /q -->

This procedure is the bench half of that choice: it watches BATDRV drive the three through the three behaviours TI's BATFET must
show, reads each FET's share of the current and each junction, and settles **D-14's gate drive with the three FETs on one BATDRV**
(register row R-183, L4-E11 row E11-37). TI's statement (Q-TI-17, extended to three devices, drafted, not sent) would replace it. A
thermal result does not close this row (the block's first line, section 2): TP-E11-29 answers a different question.

## 2. The specimen and what transfers

<!-- q src="v2/docs/records/l4e9/L4-POWER-ARCHITECTURE.md" row="E11-37 (R-183)" col="Specimen" -->
> TI's BQ25730 evaluation hardware (whether TI offers one, and its price, not read) modified as drafted, or the controlled first
> prototype of board A
<!-- /q -->

<!-- q src="v2/docs/records/l4e9/L4-POWER-ARCHITECTURE.md" row="E11-37 (R-183)" col="What transfers to the final board" -->
> only when the gate loop, the three FETs and VSYS's capacitance are the draft's; the rule: L4-E11 17d's block E11-37 (lot,
> operating point, mounting, thermal boundaries, uncertainty, permitted extrapolation, comparison rule, re-test triggers; L4-QR01)
<!-- /q -->

**Re-quoted 6 October 2026 (quotes only):** the cell read on set 30 names the three FETs (`v2/docs/records/l4e9/L4-POWER-ARCHITECTURE.md`
line 753, set 31, `v2/docs/records/l4e9/SET31-CHANGES.md`); the next sentence was written on the earlier cell, which named the pair
(quoted here on 4 October 2026, commit b367a77d), and the next set's procedures refresh (Q-07) restates it.

The cell above still names the pair; the block it points to, rebound in round 9, names the three, and this procedure follows the
block. The governing block, in full:

<!-- q src="v2/docs/records/l4e11/L4E11-SOURCE-ONLY-AND-ENTRY.md" -->
> - **Why rebound:** the owner's reviewer (4 October) read this block as covering the pair only, with transfer restricted to that
> gate network; the third FET changes the network, so the block is the three's. Thermal improvement does not close the gate-drive
> question.
>
> - **Specimen and lot:** TI's BQ25730 evaluation hardware modified as drafted, or the controlled first prototype of board A; the
> BQ25730's and the three FETs' lots recorded.
>
> - **Operating point:** supplement entry on a source removed under 0 to 10 A; the ideal diode's 30 mV regulation; LDO mode at
> VSYS_MIN with the precharge's 0.33616 A; at -20, 25 and 70 C ambient. The gate load is the three's Ciss, 7.08 nF typical at -15
> V and about 8.61 nF near 0 V (1.42 and 1.72 times TI's 5 nF); BATDRV's time constants 42.48 us on (-15 V), 51.66 us on near 0 V
> and 18.08 us off.
>
> - **Mounting and thermal boundaries:** the gate loop from BATDRV to the three gates (its length, the equal branches and any
> series element) and VSYS's capacitance as drafted; **current sharing**: each FET's drain current read (a shunt or a Hall probe
> per drain) in LDO mode and as an ideal diode, one gate node driving three thresholds; **thermal coupling**: each junction
> recorded on the shared pour; **device spacing**, **copper connectivity**, **neighbouring sources** (the charger's converter
> running as in service), **airflow** and **enclosure coupling** (a chamber's still air) recorded, because the gate's capacitance
> and the threshold move with temperature.
>
> - **Measurement uncertainty:** probes with at least 100 MHz bandwidth and short ground loops; VSYS within 1 %; each drain
> current within 2 %.
>
> - **Permitted extrapolation:** to the final board only when the gate loop, the three FETs and VSYS's capacitance are the
> draft's; a result with the pair does not transfer to the three, nor the three's to the pair.
>
> - **Re-test when:** the gate network, the FET part, lot or count, VSYS's capacitance or the charger's settings (EN_LDO,
> VSYS_MIN) change.
<!-- /q -->

**Consequences for this procedure.**

- **The specimen carries three FETs.** If TI's evaluation hardware is used, it is modified to the draft: BQ25730 pin 21 (BATDRV) to
  the gates of Q39, Q40 and Q42 from one node by equal branches (their length and any series element as drafted), the three between
  VSYS and CH_BATQ, R17 (5 mOhm) between CH_BATQ and the pack, and VSYS's capacitance as drafted (the parts as
  `v2/docs/records/l4e11/apply_gen_sch_a_charger.py` writes them for board A; at most 489 uF on VSYS, L4-E11 15b and 12e). The
  modification is recorded with photographs; any difference from the draft limits the transfer as the block states. A run with two
  FETs fitted says nothing about the three, and the reverse (the block's extrapolation line).
- **The shared pour.** The block records each junction "on the shared pour", so the three sit on one CH_BATQ drain pour and one VBAT
  source pour as board A's layout requirement draws them (L4-E11 19b, quoted in TP-E11-29 section 2). On evaluation hardware that
  is a small carrier for the three FETs, wired in by the shortest leads the bench allows (proposal); its copper is recorded.
- **Each drain's current.** The block reads each FET's drain current. With the drain tabs on one pour, the current is read in each
  FET's source connection (the same current), through a calibrated link of equal resistance per FET or a current probe on an equal
  loop per FET (proposal). The links are a difference from the draft and are kept small against the FETs' on-resistance; their
  resistance and inductance are recorded with the run, because source resistance evens the sharing and the result is read with that
  in mind.
- **Each junction.** The channel conducts during these runs, so the body diode's VSD method of TP-E11-29 does not apply. Each FET's
  junction is recorded as its drain tab's temperature (a fine thermocouple at the tab) plus its own dissipation (its current times
  the drop across it) times the sheet's printed maximum Rth(j-mb), which TP-E11-29's block quotes (proposal).
- **The gate network is the draft's.** The block's re-test line names the gate network. Round 9's draft
  `v2/docs/records/l4e11/apply_gen_sch_a_dd7.py` (register row R-217, the hardware charge inhibit) puts the drain of a small
  P-channel FET, Q49, on the same gate node. If the build is to carry that draft, the specimen carries Q49 and its gate parts too,
  with the inhibit not asserted, so Q49 is off as in normal service (proposal); the run's record states which gate network was
  tested. Q49's own function is register row R-219's bench, not this procedure's.
- The same specimen then serves TP-E11-31.

## 3. Safety

- **The pack:** a lithium-ion pack is not needed; a bidirectional DC source (a battery simulator that sources and sinks) stands for
  the pack (proposal), set to the record's voltages. If a real 4S pack is used: the laboratory's battery rules (README section 6),
  a fuse in the pack lead rated for the 10 A run, and the pack outside the chamber unless its own temperature rating covers the run.
- **Current:** up to 10 A on the battery path; leads, links and the simulator rated for it. If one FET takes most of the current
  (which this procedure exists to find out), its tab is watched: a run is stopped when a recorded junction reaches the junction
  limit the acceptance of TP-E11-29 quotes (proposal).
- **Chamber:** -20 C and 70 C runs; burns at 70 C; at -20 C, let the specimen warm in dry air before opening (condensation on a
  powered board).

## 4. Equipment, and the accuracy each measurement needs

| Item | Class | Accuracy and capability needed |
|---|---|---|
| Battery simulator | a bidirectional (source and sink) DC supply | 8 to 17 V, at least 10 A both ways; its output impedance and response recorded |
| Input supply (VBUS20) | a programmable DC supply with a fast output disable, or a supply behind a solid-state switch | 19.15 to 20.96 V (the record's VBUS20 range, L4-E11 15b); the removal edge recorded |
| Electronic load on VSYS | a DC electronic load, constant current | 0 to 10 A (the block's supplement entry) |
| Oscilloscope and probes | at least 100 MHz, short ground connections (the block) | BATDRV, the gate node and each FET's gate at its pin, VSYS and CH_BATQ; the gate measured against VSYS with a differential probe (the drive is referred to VSYS) |
| Per-FET current | a calibrated low-value link in each FET's source connection read differentially, or a clip-on current probe on an equal loop per FET (proposal) | each drain current within the block's drain-current term; where one FET carries almost nothing, the term is taken on the total current of that point (proposal); bandwidth enough to follow the supplement entry's capture (proposal: at least 1 MHz) |
| DC voltmeter for VSYS | a bench multimeter | VSYS within 1 % (the block), that is 0.12 V at 12 V, about half of the 0.246 V between VSYS_MIN's 12.3 V setting and its printed least 12.054 V; for the LDO-mode line this folder proposes 0.1 % (12 mV), well inside a quarter of 0.246 V (62 mV) |
| Drop across the three | a low-range differential voltmeter between the FETs' source and drain pins, and across each FET | the 30 mV regulation resolved within 1 mV (proposal) |
| Tab thermocouples | type T or K, fine gauge, one at each FET's drain tab, and one in the chamber air beside the specimen | within 1 K after comparison at one temperature (proposal) |
| Climatic chamber | a temperature chamber | -20, 25 and 70 C ambient (the block), still air around the specimen (the block's enclosure coupling) |
| I2C host | TI's evaluation software or a microcontroller on the BQ25730's bus | writes EN_OOA 0, VSYS_MIN, ChargeCurrent and CHRG_INHIBIT; reads the status and fault registers |
| Capacitance meter (supporting reading) | an LCR meter or a C-V analyser with a bias fixture | Ciss of the specimen's three FETs at VDS -15 V and near 0 V, information only |

## 5. Setup and measurement points

1. Specimen in the chamber; the battery simulator on the pack terminals (through R17 as drafted); VBUS20 from the input supply; the
   electronic load on VSYS; the charger's converter running as in service (the block's neighbouring sources).
2. Probe points: BATDRV at pin 21; the gate node, and each FET's gate at its pin; VSYS at the three's source pins; CH_BATQ at the
   drain tabs; the battery current (a current probe on the pack lead); each FET's current (its link or probe); each FET's tab
   thermocouple. The sum of the three FET currents is compared with the pack-lead current at one steady point before the runs; a
   difference beyond the two readings' combined uncertainty is resolved first (proposal).
3. The charger configured as the firmware rules draft it (E11-28): EN_OOA 0 at boot, VSYS_MIN 12.3 V (its POR value for 4S),
   ChargeCurrent as each step needs.
4. Record what the block lists as boundaries: the gate loop (its length, the branches, any series element, Q49 if fitted), the
   three's spacing and copper, the links, the neighbouring sources running, the airflow and the chamber.

## 6. Steps

Run the whole sequence at 25 C first, then at -20 C and 70 C, each after the specimen has soaked to the chamber's temperature
(proposal: 30 minutes after the board's thermocouple is steady within 1 K).

1. **Supplement entry.** Battery simulator at 14.4 V (proposal: a mid-charge 4S stack), VBUS20 at 20 V, the load at 0, 2, 5 and 10 A
   in turn (the block's 0 to 10 A; the points are a proposal). Remove VBUS20. Capture BATDRV, the gate node, VSYS, the battery
   current and each FET's current from 1 ms before to 50 ms after (proposal). Record: VSYS's least value; the time from removal
   until the gate is at least 8.5 V below VSYS (TI's least BATDRV drive, L4-E11 16a); any ringing or periodic component on BATDRV
   or the gates after the entry has settled; each FET's current during the entry and once it has settled. The block's BATDRV time
   constants for the three (section 2) are expectations on typical Ciss, not limits: the measured gate edges are RECORDED beside
   them.
2. **Ideal-diode regulation and sharing.** VBUS20 present with the input limit set below the load (proposal: the load 0.5 A above
   the input's limit) so the pack supplements a small current; step the supplement current in small steps (proposal: 0.1, 0.25,
   0.5, 1, 2 A), then to 5 and 10 A (proposal), where the FETs are fully on and share by their on-resistance. At each step record
   the drop across the three (the 30 mV regulation, which holds until the FETs are fully on), each FET's current and its own drop,
   and BATDRV and the gates for oscillation over at least 1 s (proposal). At 2, 5 and 10 A hold until the tab thermocouples change
   by at most 0.5 K over 5 minutes (proposal), then record each tab and each FET's current again.
3. **LDO mode and sharing.** VBUS20 present; battery simulator at 10.0 V (the pack's CUV stack) and at 8.0 V (the Shutdown Voltage);
   the charger in precharge at the record's 0.33616 A (the block). Record VSYS (DC, and its ripple), BATDRV and the gates over at
   least 10 s (proposal), each FET's current, and each tab once steady (as step 2). The FETs are linear here and dissipate; the
   record sizes this mode with the whole current in one FET (quoted in section 8), and L4-E11 12e's rule R-b' bounds when this mode
   may run.
4. **Supporting reading:** after the runs, the three FETs' Ciss (desoldered, or on spare parts of the same lot) at VDS -15 V and
   near 0 V, against the typical figures the records state for one part and for the three (section 1). Information only.

## 7. Data to record

| Ambient (C) | Load at removal (A) | VSYS least (V) | Time to full drive (us) | I Q39 / Q40 / Q42 settled (A) | Oscillation seen (yes / no, and its frequency and amplitude) |
|---|---|---|---|---|---|
| 25 | 0 | | | | |

| Ambient (C) | Supplement current (A) | Drop across the three (mV) | I Q39 / Q40 / Q42 (A) | Tab Q39 / Q40 / Q42 (C) | Junction Q39 / Q40 / Q42 (C) | Oscillation seen |
|---|---|---|---|---|---|---|
| 25 | 0.1 | | | | | |

| Ambient (C) | Pack (V) | Precharge current (A) | VSYS mean (V) and U | VSYS ripple (mV) | I Q39 / Q40 / Q42 (A) | Tab Q39 / Q40 / Q42 (C) | Junction Q39 / Q40 / Q42 (C) | Oscillation seen |
|---|---|---|---|---|---|---|---|---|
| 25 | 10.0 | | | | | | | |

Also the specimen's boundaries as built (section 5 item 4), because the block's extrapolation line compares exactly these.

## 8. Pass, fail and inconclusive

The register's acceptance and L4-E11's row, quoted:

<!-- q src="v2/docs/records/l4e9/DOWNSTREAM-REGISTER.md" row="R-183" col="Acceptance" -->
> TI's statement of what the BATFET's 5 nF bounds for three P-channel FETs on one BATDRV filed, or the bench's BATDRV behaviour
> with the three at -20, 25 and 70 C on L4-E11 17d's specimen for block E11-37: supplement entry, the ideal diode's 30 mV
> regulation without oscillation, LDO mode at VSYS_MIN within its printed band, each FET's share of the current in LDO mode and as
> an ideal diode, and each junction on the shared pour; a result with the pair does not transfer to the three; OPEN until one of
> them; on a negative answer the engineer chooses between the pair at its fallback (20.39 K/W with R17 apart) and one BUK6Y10-30P
> with a heat path through the case (L4-E11 16c's (S2), 19d)
<!-- /q -->

<!-- q src="v2/docs/records/l4e11/L4E11-SOURCE-ONLY-AND-ENTRY.md" row="E11-37" col="Acceptance" -->
> BATDRV with the three-device network Q39, Q40 and Q42 (round 9, 19d; record l9stk's C3): TI's statement of what the BATFET's 5 nF
> bounds for three P-channel FETs on one BATDRV (Ciss at which VDS, or a gate charge; Q-TI-17 extended to three, drafted in
> `clarification/TI-QUESTIONS.md`, not sent), or the bench's BATDRV behaviour with the three (Ciss 7.08 nF typical at -15 V, about
> 8.61 nF near 0 V) at -20, 25 and 70 C: supplement entry, the ideal diode's 30 mV regulation without oscillation, LDO mode at
> VSYS_MIN within its printed band, each FET's share of the current in LDO mode and as an ideal diode, and each junction on the
> shared pour; a result with the pair does not transfer; Q-TI-17 (e) and (f) (round 11, 21d) ask the 5 nF's drain-source voltage,
> the pair's typical figure and the gate load TI accepts; on a negative answer the supplier's correction scope is round 11's (ii):
> the pair at its fallback, its bar measured on the coupon, Q42 removed (a draft then owed; 16c, 19d and 21d)
<!-- /q -->

**Re-quoted 6 October 2026 (quotes only):** the cell read on set 30 (`v2/docs/records/l4e11/L4E11-SOURCE-ONLY-AND-ENTRY.md` line 727,
as L4-E11 round 11 restated it on 4 October 2026) names round 11's (ii) as the supplier's correction scope on a negative answer;
section 10's consequence is from R-183's cell above and the earlier E11-37 cell (quoted here on 4 October 2026, commit b367a77d: the
engineer chooses between the pair at its fallback and one FET with a heat path through the case), and the next set's procedures
refresh (Q-07) owns it.

- **Supplement entry:** PASS when, at each ambient and load, the three reach full drive and no oscillation is seen after the entry
  has settled. VSYS's least value is RECORDED and handed to TP-E11-31's D2 line (this row states no floor for it).
- **The ideal diode's 30 mV regulation:** PASS when the regulation holds without oscillation at every step. The band the 30 mV is judged
  against is the one SLUSE65A prints for the ideal-diode regulation if it prints one; otherwise TBD (owed by R-183): the band within
  which the regulated drop counts as "regulation", and until it is stated the drop is RECORDED.
- **LDO mode at VSYS_MIN within its printed band:** PASS when VSYS less U is at least 12.054 V at each ambient and pack voltage, and no
  oscillation is seen. The printed band's lower side is 12.054 V (VSYS_MIN_REG_ACC, 12.3 V at -2 %, SLUSE65A p.10); its upper side
  is not printed (L4-E11 12c and A11-18 take 12.546 V where a figure needs it), so VSYS's upper value is RECORDED against 12.546 V
  without a verdict:

<!-- q src="v2/docs/records/l4e11/L4E11-SOURCE-ONLY-AND-ENTRY.md" -->
> VSYS_MIN_REG_ACC prints -2 % in its maximum column as well (p.10), so its upper side is not printed; no claim rests on it (the
> floor decides each), and where a figure needs it 12.546 V is taken (A11-18)
<!-- /q -->

- **Each FET's share of the current, in LDO mode and as an ideal diode, and each junction on the shared pour:** the two acceptances
  ask for them and state no limit, so each share and each junction is RECORDED (README section 3). What makes a share or a junction
  a negative answer is TBD (owed by R-183): the share of the current, or the junction reading, at which the three's sharing counts
  as a negative answer in each mode. For LDO mode the record already takes the whole current in one FET:

<!-- q src="v2/docs/records/l4e11/L4E11-SOURCE-ONLY-AND-ENTRY.md" -->
> - The current: 0.256 x 1.30 / 0.99 = **0.33616 A** at most, all of it in one FET (linear-mode sharing is not assumed).
<!-- /q -->

- **"Without oscillation"** has no stated amplitude or duration in the records: TBD (owed by R-183): the criterion that makes a
  waveform an oscillation (a periodic component's amplitude at BATDRV or VSYS, and how long it must persist); until it is stated,
  every periodic component after settling is recorded with its frequency and amplitude, and the row's verdict waits for it.
- **FAIL** (the "negative answer"): any oscillation by the stated criterion, a failed supplement entry, or VSYS less U under 12.054 V in
  LDO mode.
- **INCONCLUSIVE:** the specimen's gate loop, its three FETs or VSYS's capacitance differ from the draft without the difference being
  recorded and accepted; fewer than three FETs fitted; a FET's current not read within the block's term; the ambient not held; the
  probes' ground loops too long to exclude probe-induced ringing (the supplier repeats with a shorter connection).

## 9. The uncertainty budget

| Term | Source | Value |
|---|---|---|
| VSYS | the block | within 1 % (0.12 V at 12 V); the proposal of section 4 tightens it to 0.1 % for the LDO-mode line |
| Each drain current | the block | its drain-current term; at a point where one FET carries almost nothing, taken on the total (proposal) |
| Probe bandwidth and grounding | the block | at least 100 MHz, short ground loops |
| The drop across the three, and across each FET | this procedure (proposal) | 1 mV |
| Tab temperature and the junction estimate | this procedure (proposal) | the thermocouple within 1 K; the junction estimate carries the printed maximum Rth(j-mb), so it is an upper estimate of the rise over the tab |
| The per-FET links | this procedure (proposal) | their resistance and inductance recorded; their evening effect on the sharing stated with the result, never corrected out |
| Ambient | the chamber | within its stated uniformity, recorded |
| The battery simulator's own response | the instrument | its output impedance recorded; a simulator slower than a pack changes the supplement entry, so the entry is repeated with a real pack if the result is near a limit (proposal) |

## 10. Consequence of a fail, and the re-test triggers

- **A negative answer** sends the choice to the engineer, between the pair at its fallback and one BUK6Y10-30P with a heat path
  through the case (R-183, quoted in section 8; L4-E11 16c and 19d). TP-E11-29 then reads the chosen arrangement, the pair against
  its fallback figure; one FET with a case path is a different specimen.
- **TI's statement** of what the 5 nF bounds for three FETs on one BATDRV (Q-TI-17, extended) closes the row without this test.
- **A result with the pair does not transfer to the three, nor the three's to the pair** (the block and R-183).
- **Re-test triggers:** the block's "Re-test when" line (section 2): the gate network, the FET part, lot or count, VSYS's capacitance
  or the charger's settings (EN_LDO, VSYS_MIN) change.

## 11. Authorisation and purchases (nothing has been bought)

<!-- q src="v2/docs/records/l4e9/L4-POWER-ARCHITECTURE.md" row="E11-37 (R-183)" col="Authorisation" -->
> the owner's: the evaluation hardware and parts; Q-TI-17 to TI
<!-- /q -->

<!-- q src="v2/docs/records/l4e9/L4-POWER-ARCHITECTURE.md" row="E11-37 (R-183)" col="What to buy" -->
> BUK6Y10-30PX (the samples of E11-29's two coupons of three, E11-30's six pulsed parts, E11-36's Kelvin coupon, E11-37's three,
> four spare), Nexperia: 3 of the 23 at 1.7386 USD each (the 10-piece tier, LCSC C3278350, stock 67 on 2 October 2026;
> v2/docs/records/l4e11/inputs/lcsc-C3278350-2026-10-02.json); price not read: TI's BQ25730 evaluation hardware, whether TI offers
> one; BQ25730RSNR (LCSC C5219071, 2.8553 USD at 1 but stock 0 on 2 October 2026: an authorised source, its price not read)
<!-- /q -->

What to send (5d): Q-TI-17, as extended to three devices in round 9, in `v2/docs/records/l4e11/clarification/TI-QUESTIONS.md` (the
owner sends it). The carrier for the three FETs, the per-FET links or probes and the tab thermocouples are the supplier's quotation
items.
