meshsat/meshsat-fieldkit/v2/docs/test-procedures/TP-E11-30.md

# TP-E11-30: the docking pulse in one body diode (six BUK6Y10-30PX, 2000 pulses each)

<!-- tp
id: TP-E11-30
title: The docking pulse in one body diode (six BUK6Y10-30PX, 2000 pulses each)
register: R-160
e11: E11-30
route5d: E11-30 (R-160)
-->

**Status: PROPOSED, for the supplier to review and agree before execution.** MESHSAT-1357, 3 October 2026. Prototype design:
nothing here has been built, bought, powered or measured. Common rules: `v2/docs/test-procedures/README.md`.

## 1. Purpose and the decision it settles

When the pack's discharge FET switches onto an empty VSYS (a docking event), the inrush passes through one battery FET's body
diode. The record describes the waveform and why a junction-temperature calculation cannot accept it:

<!-- q src="v2/docs/records/l4e11/L4E11-SOURCE-ONLY-AND-ENTRY.md" -->
> A junction-temperature calculation does not extend ISM's printed rating (320 A, single pulse, tp at most 10 us, Tmb 25 C; Table
> 5, p.3). The waveform to accept: **242.9 A peak, time constant 33.8 us**, over IS's 80 A for 37.6 us, from a +70 C mounting
> base, once per docking event (the pack's discharge FET switching onto an empty VSYS), taken whole in one FET's body diode.
<!-- /q -->

The record selected a defined pulse qualification on parts (its option D2), with Nexperia's written acceptance (Q-NXP-1, drafted,
not sent) asked in parallel and board P's inrush limit (D3) as the fallback. This procedure is that qualification. It settles
**D-14's docking pulse** (register row R-160, L4-E11 row E11-30) and gates only board A's final release.

## 2. The specimen and what transfers

<!-- q src="v2/docs/records/l4e9/L4-POWER-ARCHITECTURE.md" row="E11-30 (R-160)" col="Specimen" -->
> six BUK6Y10-30PX samples on single-device coupons on a heated mounting base, and a capacitor-discharge rig
<!-- /q -->

<!-- q src="v2/docs/records/l4e9/L4-POWER-ARCHITECTURE.md" row="E11-30 (R-160)" col="What transfers to the final board" -->
> to the build only for the tested lot and inside the tested envelope; prototype evidence, not a production limit; the rule:
> L4-E11 17d's block E11-30 (lot, operating point, mounting, thermal boundaries, uncertainty, permitted extrapolation, comparison
> rule, re-test triggers; L4-QR01)
<!-- /q -->

The governing block, in full:

<!-- q src="v2/docs/records/l4e11/L4E11-SOURCE-ONLY-AND-ENTRY.md" -->
> - **Specimen:** six BUK6Y10-30PX, one per coupon, each on a heated block.
>
> - **Lot:** the six from one reel and date code, recorded; the result is **prototype evidence for that lot and those conditions,
> not a production limit**, and it does not extend Nexperia's limiting values (AN11158 2.4): the build's parts are taken from the
> tested lot, or the test is repeated on the build's lot.
>
> - **Operating point (the waveform):** 267.2 A peak, time constant 37.2 us (1.1 x the docking waveform's 242.9 A and 33.8 us),
> 2000 pulses 10 s apart (a lifetime allowance of 1000 docking events, twice), the whole pulse in one body diode.
>
> - **Mounting:** each part soldered to a coupon whose mounting-base pad sits on a block held at 75 C.
>
> - **Thermal boundaries:** the mounting base at **75 C** (over the +70 C mixed air at docking, when no current flows before the
> pulse); **device spacing** none (a single device, as the record takes the whole pulse in one FET); **copper connectivity** the
> pad and the block; **neighbouring sources**, **airflow** and **enclosure coupling** enter only through the mounting base's
> starting temperature, which the block sets: within the pulse's few hundred microseconds the heat stays inside the package (16d,
> Fig. 4's reading), a reading the test itself does not establish for longer pulses.
>
> - **Measurement uncertainty:** the peak current within 2 % (a calibrated shunt or probe), the time constant within 5 %, the
> block within 2 K; the envelope is set so that the waveform less its uncertainty still covers 242.9 A and 33.8 us.
>
> - **Permitted extrapolation:** none outside the tested envelope and lot: a docking event in the kit is covered only when its
> peak, time constant and starting mounting-base temperature are each at most the tested values and the count stays under 2000.
>
> - **Comparison with the final board:** the first prototype's docking waveform is measured (peak, time constant, the FET's
> mounting-base temperature at the event) and compared value by value with the tested envelope; no equivalence is assumed from the
> layout.
>
> - **Re-test when:** another lot or part; the prototype's measured peak, time constant or mounting-base temperature exceeds the
> tested ones; the pack loop or VSYS's capacitance changes; the expected count of docking events passes 2000.
<!-- /q -->

**Consequences for this procedure.** The six parts come from one reel and date code, and the build's parts are taken from that
lot or the test is repeated on the build's lot. The result covers a docking event only when its peak, time constant and starting
mounting-base temperature are each at most the tested values and the count stays under 2000; the first prototype's own docking
waveform is measured and compared value by value (TP-E11-30 does not measure it; it belongs to board A's first-prototype
verification and is named in the block above).

## 3. Safety

- **Stored energy.** The rig is a charged capacitor bank switched into the specimen. Its voltage and energy are the rig designer's;
  the bank has a bleed resistor, a visible charge indicator, an interlocked enclosure, and is discharged and shorted before any
  hand enters the enclosure.
- **Pulse current** to about 270 A: the leads and the switch are rated for it; magnetic forces on loose leads; eye protection
  against a failing part (a body diode can fail short or open violently under an over-stress).
- **Unattended pulsing** (about 5.6 h per part): an automatic abort on a missed or abnormal pulse (a peak or time constant outside
  the validity window of section 8), on the block's temperature leaving its window, or on a specimen short.
- **Hot block** at 75 C: burn protection when changing parts.

## 4. Equipment, and the accuracy each measurement needs

| Item | Class | Accuracy and capability needed |
|---|---|---|
| Capacitor-discharge pulse rig | a capacitor bank, a pulse switch and a series resistance, laboratory-built or a commercial surge-current tester | an exponential pulse of 267.2 A peak and a 37.2 us time constant, repeatable at one pulse every 10 s for 2000 pulses; the setting adjustable so every pulse falls inside section 8's validity window |
| Pulse current measurement | a coaxial current shunt or a calibrated wide-band current transformer | the peak within 2 % (the block); its 10 to 90 % rise time at most a tenth of the pulse's measured rise (proposal), so the peak is not filtered |
| Digitiser or oscilloscope | 12-bit or better | sampling at 10 MS/s or faster (proposal: more than 300 samples per time constant), so the time constant is fitted within 5 % (the block) |
| Voltage across the specimen during the pulse | a differential probe at the part's pins | recorded per pulse: the forward voltage at the peak (information; a rising trend is reported) |
| Heated mounting block | a temperature-controlled block with its own sensor and a thermocouple at the mounting-base pad | the block within 2 K (the block); set to 75 C |
| Pre and post electrical tests | a power-device curve tracer or source-measure units with a pulsed high-current module | VSD at 80 A pulsed and RDS(on) at -10 V repeatable to 1.25 % or better (proposal: a quarter of the 5 % change they are judged against); IDSS at -30 V read with an expanded uncertainty of at most 0.25 uA, a quarter of the printed 1 uA (proposal); IGSS with at most 25 nA, a quarter of the printed 100 nA (proposal); each at the test conditions the sheet prints for its row (BUK6Y10-30P, Nexperia, 17 April 2020, Table 7, p.6; held back from this tree, fetched by `v2/docs/records/l4e11/fetch_held_back.py`) |

## 5. Setup and measurement points

1. **Six single-device coupons**, each with one BUK6Y10-30PX soldered as on board A (its mounting-base pad joined to a land that sits
   on the heated block), short low-inductance leads to the rig. Record the coupon's fabricator, copper weight and the solder process.
2. **The pulse path:** the rig's output into the part's drain-to-source direction that forward-biases its body diode (a P-channel
   part: drain positive; the supplier confirms against the sheet's symbol), gate tied to source.
3. **Measurement points:** the pulse current (the shunt or transformer in the return path); the voltage across the part at its pins;
   the block's sensor and the mounting-base thermocouple.

## 6. Steps

1. **Identity.** Record the reel and the date code of all six parts (one reel, one date code). Number them P1 to P6.
2. **First readings at 25 C**, each part, before any pulse: VSD at 80 A pulsed; IDSS at -30 V; RDS(on) at -10 V; IGSS. These are each
   part's own baseline ("its first reading").
3. **Set the rig** on a dummy (a sacrificial part of the same type, not one of the six): adjust until ten consecutive pulses each fall
   inside the validity window of section 8 and read 267.2 A and 37.2 us at the setting. Record the setting.
4. **Mount P1** on its coupon on the block at 75 C; wait until the mounting-base thermocouple is steady within 0.5 K over 5 minutes
   (proposal).
5. **Pulse:** 2000 pulses, one every 10 s. For every pulse record the peak, the time constant (an exponential fitted to the decay from
   the peak to 10 % of it; proposal), the forward voltage at the peak and the mounting-base temperature just before the pulse. A pulse
   outside the validity window is not counted and is repeated; more than 20 such pulses on one part (proposal) stop the run as
   INCONCLUSIVE for the rig to be corrected.
6. **Cool** the part to 25 C and repeat the four readings of step 2.
7. **Repeat** steps 4 to 6 for P2 to P6.
8. **Reduce:** per part, each post-test reading against its first reading and against the printed limit, with U.

## 7. Data to record

| Part | Reel and date code | Pulses counted | Pulses rejected | Peak, least and greatest (A) | Time constant, least and greatest (us) | Block, least and greatest (C) |
|---|---|---|---|---|---|---|
| P1 | | | | | | |

| Part | VSD at 80 A before / after (V), change (%) and U | IDSS at -30 V after (uA) and U | RDS(on) at -10 V before / after (mOhm), change (%) and U | IGSS after (nA) and U | Verdict |
|---|---|---|---|---|---|
| P1 | | | | | |

The per-pulse log (pulse number, peak, time constant, forward voltage at the peak, block temperature) is kept as a file.

## 8. Pass, fail and inconclusive

The register's acceptance and L4-E11's row, quoted:

<!-- q src="v2/docs/records/l4e9/DOWNSTREAM-REGISTER.md" row="R-160" col="Acceptance" -->
> Every part passes VSD at 80 A pulsed within +5 % of its first reading, IDSS at -30 V and 25 C at most the printed 1 uA, RDS(on)
> at -10 V and 25 C within +5 % and at most the printed 10 mOhm, IGSS at most the printed 100 nA (a sample result, not a
> production limit); or Nexperia's acceptance of the waveform filed; a failure moves to (D3): board P's owner constrains the pulse
> with a slower discharge-FET turn-on or a precharge path whose turn-off under ASCD and normal charging are shown unchanged;
> prototype evidence for the tested lot and inside the tested envelope only (L4-E11 17d, block E11-30, L4-QR01; Nexperia AN11158
> 2.4): the build's parts from the tested lot or the test repeated on the build's lot, the first prototype's docking waveform
> (peak, time constant, mounting-base temperature) measured and compared value by value, no equivalence assumed from the layout;
> never a production limit or an extension of Nexperia's limiting values
<!-- /q -->

<!-- q src="v2/docs/records/l4e11/L4E11-SOURCE-ONLY-AND-ENTRY.md" row="E11-30" col="Acceptance" -->
> the WHOLE hot docking waveform accepted (sections 16d and 17b): 242.9 A peak, time constant 33.8 us, from a +70 C mounting base,
> once per docking event, taken whole in one FET's body diode; by the pulse qualification selected in 17b: 6 parts, each 2000
> pulses 10 s apart at 267.2 A peak and 37.2 us (x1.1), mounting base 75 C, every part passing VSD at 80 A pulsed within +5 % of
> its first reading, IDSS at -30 V and 25 C at most the printed 1 uA, RDS(on) at -10 V and 25 C within +5 % and at most the
> printed 10 mOhm, IGSS at most the printed 100 nA; or Nexperia's written acceptance of the same waveform (Q-NXP-1); a sample
> result is not a production limit; on a failure board P's owner bounds the inrush (a slower discharge-FET turn-on or a precharge
> path, its normal charging and its ASCD turn-off re-shown)
<!-- /q -->

- **Validity of each pulse** (from the block: "the envelope is set so that the waveform less its uncertainty still covers 242.9 A and
  33.8 us"): a pulse counts when its peak less U is at least 242.9 A and its time constant less U is at least 33.8 us, and the
  mounting base reads 75 C. With the block's 2 % and 5 % the setting of 267.2 A and 37.2 us leaves 261.9 A and 35.3 us at the least,
  inside that window. A pulse whose peak or time constant exceeds the setting by more than the rig's stated repeatability stresses the
  part beyond the plan: if a part fails after such pulses its run is INCONCLUSIVE, not a FAIL of the part (proposal).
- **Validity of the base temperature:** the mounting base stands for the +70 C mixed air at docking (the block: "the mounting base at
  **75 C** (over the +70 C mixed air at docking, when no current flows before the pulse)"); a pulse delivered with the base reading
  less its 2 K under +70 C is not counted (this folder's reading of that sentence).
- **PASS** for the row when all six parts, after 2000 counted pulses each, meet every line of the acceptance above with U taken
  against each line (README section 3): the VSD change plus its U at or under +5 %; IDSS plus U at or under 1 uA; the RDS(on) change
  plus U at or under +5 % and RDS(on) plus U at or under 10 mOhm; IGSS plus U at or under 100 nA.
- **FAIL** when any part fails any line on a valid run.
- **INCONCLUSIVE** when a run is stopped (section 6 step 5), the lot is mixed, or the pre-test reading of a part is itself outside the
  printed limits (that part is replaced from the same reel and the replacement recorded).
- A fall of VSD or RDS(on) is not bounded by the acceptance: TBD (owed by R-160): whether a fall beyond the measurement's uncertainty
  counts as a failure; until stated, any such fall is reported with the part's data and no verdict is drawn from it.

## 9. The uncertainty budget

| Term | Source | Value |
|---|---|---|
| Pulse peak | the block | within 2 % |
| Time constant | the block | within 5 % |
| Mounting-base temperature | the block | within 2 K |
| VSD at 80 A, RDS(on) at -10 V (the before and after change) | the curve tracer's repeatability and its contact resistance to the part, the same fixture both times | target 1.25 % (proposal) |
| IDSS, IGSS | the source-measure unit's range accuracy and the fixture's leakage, measured open | targets 0.25 uA and 25 nA (proposal) |
| The part's temperature during the 25 C readings | the room or a stage at 25 C | stated with the run |

## 10. Consequence of a fail, and the re-test triggers

- **A fail** moves the decision to the record's option (D3): board P's owner bounds the inrush, quoted:

<!-- q src="v2/docs/records/l4e11/L4E11-SOURCE-ONLY-AND-ENTRY.md" -->
> *Reverse:* a failure moves to (D3), board P's owner. **STATUS: CONDITIONAL on E11-30.**
<!-- /q -->

- **Nexperia's written acceptance** of the same waveform (Q-NXP-1) closes the row for every lot without this test (R-160 above).
- **Re-test triggers:** the block's "Re-test when" line (section 2): another lot or part; the prototype's measured peak, time
  constant or mounting-base temperature over the tested ones; a change of the pack loop or of VSYS's capacitance; more than 2000
  expected docking events.

## 11. Authorisation and purchases (nothing has been bought)

<!-- q src="v2/docs/records/l4e9/L4-POWER-ARCHITECTURE.md" row="E11-30 (R-160)" col="Authorisation" -->
> the owner's: the parts and the rig; Q-NXP-1 to Nexperia
<!-- /q -->

<!-- q src="v2/docs/records/l4e9/L4-POWER-ARCHITECTURE.md" row="E11-30 (R-160)" col="What to buy" -->
> BUK6Y10-30PX (the samples of E11-29's two coupons of three, E11-30's six pulsed parts, E11-36's Kelvin coupon, E11-37's three,
> four spare), Nexperia: 6 of the 23 at 1.7386 USD each (the 10-piece tier, LCSC C3278350, stock 67 on 2 October 2026;
> v2/docs/records/l4e11/inputs/lcsc-C3278350-2026-10-02.json); price not read: a capacitor-discharge rig and a heated mounting
> base
<!-- /q -->

What to send, in parallel (5d): Q-NXP-1 in `v2/docs/records/l4e11/clarification/TI-QUESTIONS.md` (the owner sends it).
