meshsat/meshsat-fieldkit/v2/docs/test-procedures/TP-E11-31.md

# TP-E11-31: source-only start and the held states on the BQ25730 (U-04)

<!-- tp
id: TP-E11-31
title: Source-only start and the held states on the BQ25730 (U-04)
register: R-161
e11: E11-31
route5d: E11-31 (R-161)
-->

**Status: PROPOSED, for the supplier to review and agree before execution.** MESHSAT-1357, 3 October 2026. Prototype design:
nothing here has been built, bought, powered or measured. Common rules: `v2/docs/test-procedures/README.md`.

## 1. Purpose and the decision it settles

The kit must run from a source alone (a dead or absent pack, a held pack) and must start from cold that way. The drafted charger
is TI's BQ25730, whose three modes the record bounds on the maker's printed rows, except where the sheet prints nothing:

<!-- q src="v2/docs/records/l4e11/L4E11-SOURCE-ONLY-AND-ENTRY.md" -->
> So on held evidence the start ends in VSYS_MIN or in a latch within 3.062 s, never undefined. Whether the first window succeeds
> is not bounded (no minimum delivered current is printed): **bench E11-31**, acceptance: from cold, at VBUS20 19.15 and 20.96 V,
> with VSYS's maximum capacitance and the declared always-on loads (board E on VSYS_E), at -20, 25 and 62.1 C, VSYS reaches 12.054
> V with Fault VSYS_UVP clear; the hiccup's 500 / 10 ms and the latch shown on a shorted VSYS and cleared by a re-plug.
<!-- /q -->

<!-- q src="v2/docs/records/l4e11/L4E11-SOURCE-ONLY-AND-ENTRY.md" -->
> **So each mode has the maker's printed bound on VSYS: D1 and D3 are removed.** The margin from the floor to A-14's assumed 10.0
> V converter floor is 2.054 V, which a load step in S2 or S4 must not use up: that is D2, and SLUSE65A prints no transient limit
> either (Figure 9-22, p.96, draws the peak power mode on VSYS undershoot, 1 to 6 A at VSYS_MIN 12.3 V with ICHG 0 A, at 4 ms a
> division, a scale that resolves no transient).
<!-- /q -->

This procedure measures the three modes, the held pack current, the start from cold and D2 (VSYS's step response) and settles
**U-04** (register row R-161, L4-E11 row E11-31): its move from a closure condition to a downstream qualification test once R-157,
R-177 and R-178 are applied (5d). It gates board A's final release; the charger's firmware rules (R-158) are written to the draft
meanwhile.

## 2. The specimen and what transfers

<!-- q src="v2/docs/records/l4e9/L4-POWER-ARCHITECTURE.md" row="E11-31 (R-161)" col="Specimen" -->
> E11-37's specimen (TI's BQ25730 evaluation hardware set as drafted, or the controlled first prototype of board A) with a board E
> stub on VSYS_E (U12, C31, U22's 12.0 V rail with its capacitors C142 to C148 and the four-wire fan headers) and the pack or a
> pack simulator
<!-- /q -->

<!-- q src="v2/docs/records/l4e9/L4-POWER-ARCHITECTURE.md" row="E11-31 (R-161)" col="What transfers to the final board" -->
> the charger's register behaviour and VSYS's modes (device properties) fully; the start's first window and D2's recovery only
> where VSYS's capacitance and the always-on loads are the draft's; otherwise re-read on the first prototype
<!-- /q -->

L4-E11 section 17d has no block of its own for this row; the specimen is TP-E11-37's (its block applies to the charger, the three
battery FETs Q39, Q40 and Q42 since L4-E11's round 9, and VSYS's capacitance). **Consequences for this procedure.** The charger's register behaviour and the modes transfer as device
properties. The start's first window and D2's recovery transfer only where VSYS's capacitance (at most 489 uF, L4-E11 15b) and the
always-on loads are the draft's; the board E stub therefore carries U12, C31, U22's 12.0 V rail with C142 to C148 (C135 to C141
until set 28, renumbered by L4-E11 18a after they collided with the solar guard's port bank) and the fan headers, loaded to the declared currents (VSYS_E's 1.32 A at the floor: U12 0.8 A and U22 0.52 A, L4-E11 E11-33), and VSYS_E is
fed through U42 and its network as drafted (proposal: the same parts as TP-E11-38's coupon), so the start sees the eFuse's own
inrush ramp. Any difference from the draft is recorded, and the affected figures are then re-read on the first prototype.

## 3. Safety

- **The pack:** a battery simulator that sources and sinks (proposal) stands for the pack; a real 4S pack only under the laboratory's
  battery rules (README section 6) with a fuse in its lead.
- **Shorted VSYS (the hiccup and latch run):** the short is applied with VSYS discharged and the source off, then the source is
  plugged; the short is a rated low-resistance link, not a probe tip.
- **Load steps up to about 48 W at VSYS:** the electronic load and the leads rated for it; the load's own protection set.
- **Chamber** at -20 C and 62.1 C: burns; condensation when opening cold.

## 4. Equipment, and the accuracy each measurement needs

| Item | Class | Accuracy and capability needed |
|---|---|---|
| Input supply (VBUS20) | a programmable DC supply with a fast output switch | 19.15 and 20.96 V (L4-E11 15b); the plug edge recorded |
| Battery simulator | a bidirectional DC supply | 8 to 17 V both ways; for S2 a sink-only setting (the pack takes charge but cannot discharge), or a series ideal diode oriented that way (proposal) |
| Electronic load on VSYS | a DC electronic load with a dynamic (step) mode | each declared step of L4-E11 11a at its VSYS power, at the load's fastest slew (proposal), its slew recorded |
| VSYS, DC | a bench multimeter | 0.1 % (proposal): the narrowest band judged is 2 % of VSRN + 150 mV, at least 0.24 V wide on each side at 12 V, and a quarter of that is 0.06 V (0.5 %) |
| VSYS, transient | an oscilloscope with an offset or a high-resolution channel | U at most 0.1 V on the step minimum (proposal), against the 2.054 V margin (a quarter of it is 0.51 V) |
| Pack current | a multimeter on a microampere-to-milliampere range, or a calibrated shunt and a microvolt meter | U at most 0.05 mA (proposal), against the 1 mA line (a quarter of it is 0.25 mA) |
| I2C host | TI's evaluation software or a microcontroller | writes EN_OOA, VSYS_MIN, ChargeCurrent, CHRG_INHIBIT; reads the status and fault registers (Fault VSYS_UVP) with a timestamp |
| Climatic chamber | a temperature chamber | -20, 25 and 62.1 C (the row) |

## 5. Setup and measurement points

1. The specimen of TP-E11-37 with the board E stub; the battery simulator on the pack terminals through R17; VBUS20 from the input
   supply; the electronic load on VSYS for the steps.
2. Measurement points: VSYS at the battery FETs' source pins (DC and transient); SRN (the pack side of R17); the pack current in the pack
   lead; VSYS_E on the stub; VBUS20; BATDRV (information).
3. Firmware rules as drafted (E11-28, quoted in TP-E11-37's setup): EN_OOA 0 written at boot, with VSYS recorded before that write.

## 6. Steps

Each block runs at 25 C, then -20 C and 62.1 C, after the soak (proposal: 30 minutes with the board steady within 1 K).

1. **Pack absent (S4).** Pack terminals open. VBUS20 at 19.15 V, then 20.96 V. With the stub's always-on loads, read VSYS (DC) after
   EN_OOA 0 is written. Record VSYS before the write as well.
2. **Charge inhibited, pack present.** CHRG_INHIBIT 1. The simulator set in turn to SRN 10.0, 12.0, 12.3, 12.6, 14.4 and 16.8 V
   (proposal: each region of L4-E11 15d and its edges). Read VSYS at each.
3. **The held pack current.** At SRN 14.4 V and 16.8 V (proposal), CHRG_INHIBIT 1, board E on VSYS_E: read the pack current after it
   has settled (proposal: the mean over 5 minutes, 10 minutes after the setting). Record its sign: out of the pack (the drain the row
   bounds) or into it.
4. **Start from cold.** Pack absent; VSYS discharged to under 0.1 V (proposal); VBUS20 plugged at 19.15 V, then at 20.96 V. Capture
   VSYS from the plug to 5 s after (proposal), read Fault VSYS_UVP, and record the time to 12.054 V. Ten starts at each voltage and
   ambient (proposal), because the record cannot bound the first window.
5. **Hiccup and latch.** VSYS shorted, VBUS20 plugged: capture the converter's on and off times (500 ms off, 10 ms on, L4-E11 15b) and
   the latch after the 7th failure inside 90 s; remove the short; confirm the latch holds; re-plug VBUS20 and confirm the start.
6. **D2, the step response in S2 and S4.** S4: pack absent. S2: the simulator sink-only at 14.4 V (proposal). VBUS20 at 19.15 V (the
   low end, proposal). Apply each declared step of L4-E11 11a (the table below) from the stub's always-on load, ten times each
   (proposal); capture VSYS's minimum and the recovery time.

<!-- q src="v2/docs/records/l4e11/L4E11-SOURCE-ONLY-AND-ENTRY.md" -->
> **The kit's own steps** (r4a's loop design, recovered by L4-E8, session targets INFERRED there; efficiencies from gen_sch_a.py;
> the mat from hc2), at VSYS, and whether R-c's envelope admits each on top of P1's plan (19.57 W) at the widest source (36 V,
> 84.55 W):
>
> | Step | At VSYS | In S4 | Held by the fallback |
> |---|---|---|---|
> | slot rail +5V_S2, 3 A at 5.09 V (a 5G burst; 0.90 ASSUMPTION) | 16.97 W | admitted | 3.187 ms |
> | device rail +5V_DEV, 3 A at 5.09 V | 16.97 W | admitted | 3.187 ms |
> | PA rail, 5.4 A at 13.76 V (a 30 W carrier keyed) | 79.9 W | not admitted (R-c holds it) | 0.677 ms |
> | HF rail, 2 A at 12 V | 25.81 W | admitted | 2.095 ms |
> | PoE rail, 0.6 A at 54 V | 36.82 W | admitted | 1.469 ms |
> | USB-C PD outlet, 3 A at 15 V | **48.39 W** | admitted (the worst) | **1.117 ms** |
> | the pack heater mat, regulated | 8.5 W | admitted | 6.361 ms |
<!-- /q -->

## 7. Data to record

| Ambient (C) | Mode | VBUS20 (V) | SRN (V) | VSYS (V) and U | Line it is judged against | Verdict |
|---|---|---|---|---|---|---|
| 25 | pack absent | 19.15 | open | | at least 12.054 V | |
| 25 | inhibited | 20.0 | 14.4 | | VSRN + 150 mV within 2 % | |

| Ambient (C) | SRN (V) | Pack current (mA), sign, and U | Verdict |
|---|---|---|---|
| 25 | 14.4 | | |

| Ambient (C) | VBUS20 (V) | Start n | Time to 12.054 V (ms) | Fault VSYS_UVP | VSYS before EN_OOA's write (V) | Verdict |
|---|---|---|---|---|---|---|
| -20 | 19.15 | 1 | | | | |

| State | Step (L4-E11 11a) | Power at VSYS (W) | Load slew (A/us) | VSYS before (V) | VSYS minimum (V) and U | Recovery (ms) | Over 10.0 V? |
|---|---|---|---|---|---|---|---|
| S4 | USB-C PD outlet | 48.39 | | | | | |

## 8. Pass, fail and inconclusive

The register's acceptance and L4-E11's row, quoted:

<!-- q src="v2/docs/records/l4e9/DOWNSTREAM-REGISTER.md" row="R-161" col="Acceptance" -->
> Pack absent, VSYS at least 12.054 V; inhibited with SRN over 12.546 V, VSRN plus 150 mV within 2 %, SRN under 12.054 V at least
> 12.054 V, between at least 11.96 V; the held pack current at most 1 mA; from cold at VBUS20 19.15 and 20.96 V, VSYS's maximum
> capacitance and the always-on loads, at -20, 25 and 62.1 C, VSYS reaches 12.054 V with Fault VSYS_UVP clear; the hiccup and the
> latch on a shorted VSYS and the re-plug; VSYS before EN_OOA's write recorded; every step's minimum over the converters' assumed
> 10.0 V floor (the 2.054 V margin), else R-c's step rule
<!-- /q -->

<!-- q src="v2/docs/records/l4e11/L4E11-SOURCE-ONLY-AND-ENTRY.md" row="E11-31" col="Acceptance" -->
> the three modes on the BQ25730 build (EN_OOA 0), piecewise (section 15d): pack absent, VSYS at least 12.054 V; CHRG_INHIBIT 1
> with SRN over 12.546 V, VSRN plus 150 mV within 2 percent, under 12.054 V at least 12.054 V, between at least 11.96 V; the held
> pack current at most 1 mA with board E on VSYS_E; the start from cold at VBUS20 19.15 and 20.96 V, VSYS's maximum capacitance
> and the always-on loads, at -20, 25 and 62.1 C, with Fault VSYS_UVP clear, the hiccup and latch on a shorted VSYS and the
> re-plug; VSYS before EN_OOA's write recorded; VSYS's step response in S2 and S4 for each declared step against the converters'
> floor (D2, 2.054 V of margin), the outlets held by R-c where a step uses more
<!-- /q -->

- **Pack absent:** PASS when VSYS less U is at least 12.054 V at every input voltage and ambient.
- **Inhibited:** PASS per region: SRN over 12.546 V, VSYS within VSRN + 150 mV plus or minus 2 % with U inside the band; SRN under
  12.054 V, VSYS less U at least 12.054 V; between, VSYS less U at least 11.96 V.
- **The held pack current:** PASS when the current out of the pack plus U is at most 1 mA at every point. A current into the held pack
  is recorded; TBD (owed by R-161): whether a current into the held pack counts against the 1 mA.
- **The start:** PASS when every start reaches 12.054 V with Fault VSYS_UVP clear at each input voltage and ambient; the time is
  RECORDED. One start that latches or reports the fault is a FAIL of the start at that point.
- **Hiccup and latch:** PASS when the hiccup and the latch are shown and the re-plug clears the latch.
- **VSYS before EN_OOA's write:** RECORDED.
- **D2:** each declared step whose VSYS minimum less U stays over 10.0 V is admitted in that state; a step that does not is assigned to
  R-c's step rule (not admitted while the pack cannot discharge), as the row says ("else R-c's step rule"). The result is the list of
  admitted steps per state, and the row passes when every step the kit's firmware will admit in S2 and S4 is shown over 10.0 V.
  The bench's step uses the load's fastest slew; TBD (owed by R-161): the declared steps' rise times, needed only if a step fails at
  the bench's slew and the real load is slower.
- **INCONCLUSIVE:** the specimen's VSYS capacitance or always-on loads differ from the draft without the difference recorded; the
  ambient not held; EN_OOA not written before the reading the line applies to.

## 9. The uncertainty budget

| Term | Source | Value |
|---|---|---|
| VSYS DC | the meter | 0.1 % (proposal) |
| VSYS transient minimum | the scope chain (gain, offset, probe) | 0.1 V (proposal) |
| Pack current | the meter or shunt | 0.05 mA (proposal) |
| SRN setting | the simulator's readback, checked by the meter | 0.1 % (proposal) |
| Ambient | the chamber | its stated uniformity |
| The always-on loads | the electronic loads on the stub | their setting accuracy, recorded |

## 10. Consequence of a fail, and the re-test triggers

- **A mode line failed** (VSYS under its printed bound) contradicts the maker's printed row the record relies on (L4-E11 12c): the
  result goes to TI with Q-TI-15 and Q-TI-16, and U-04 returns to a closure condition (the record's fallback for a VSYS with no battery
  is the hold-up bank of L4-E11 11a, register row E11-24, never applied).
- **The held current over 1 mA:** the drains are not bounded on held evidence beyond the quantified 0.1408 mA (L4-E11 16e); the
  excess is traced (D3's hot leakage, the body diodes) and the hold's endurance re-derived.
- **A start that fails or latches:** the source-only start is not shown; the first window is the open item (L4-E11 15b).
- **A step under 10.0 V:** that step is not admitted in S2 and S4 (R-c), and the bridge's rule is written to the measured list.
- **Re-test triggers** (proposal, after TP-E11-37's block, whose triggers this specimen shares): the gate network, the FET part, lot or
  count, VSYS's capacitance, the charger's settings (EN_LDO, VSYS_MIN), the always-on loads or U42's network change.

## 11. Authorisation and purchases (nothing has been bought)

<!-- q src="v2/docs/records/l4e9/L4-POWER-ARCHITECTURE.md" row="E11-31 (R-161)" col="Authorisation" -->
> the owner's: the evaluation hardware; Q-TI-15 and Q-TI-16 to TI
<!-- /q -->

<!-- q src="v2/docs/records/l4e9/L4-POWER-ARCHITECTURE.md" row="E11-31 (R-161)" col="What to buy" -->
> price not read: TI's BQ25730 evaluation hardware, whether TI offers one; BQ25730RSNR (LCSC C5219071, 2.8553 USD at 1 but stock 0
> on 2 October 2026: an authorised source, its price not read)
<!-- /q -->

What to send (5d): Q-TI-15 and Q-TI-16 in `v2/docs/records/l4e11/clarification/TI-QUESTIONS.md`, and the battery packet
`v2/docs/review-packets/battery/REVIEW-REQUEST.md` (the owner sends them).
