meshsat/meshsat-fieldkit/v2/docs/test-procedures/TP-E11-38.md

# TP-E11-38: the eFuse U42 and the dock's VSYS branch through the fault envelope, cases (a) to (h)

<!-- tp
id: TP-E11-38
title: The eFuse U42 and the dock's VSYS branch through the fault envelope, cases (a) to (h)
register: R-184
e11: E11-38
route5d: E11-38 (R-184)
-->

**Status: PROPOSED, for the supplier to review and agree before execution.** MESHSAT-1357, 3 October 2026. Prototype design:
nothing here has been built, bought, powered or measured. Common rules: `v2/docs/test-procedures/README.md`.

## 1. Purpose and the decision it settles

Board A feeds board E's auxiliary domain (VSYS_E) over one dock contact through a TI TPS16630 eFuse, U42. The branch:

<!-- q src="v2/docs/records/l4e11/L4E11-SOURCE-ONLY-AND-ENTRY.md" -->
> **The branch:** VBAT (VSYS) on board A to J_DOCK pin 1, one Preci-Dip 813 (3.5 A operating maximum, 85 C with its music-wire
> spring), its 24 AWG and board E's copper to VSYS_E; 1.0 A declared. The review's counterexample, 5 A from 14.4 V (2.88 Ohm), is
> over the contact and under every upstream threshold, in source-only and battery operation alike; the 1 A declaration limits
> nothing.
<!-- /q -->

<!-- q src="v2/docs/records/l4e11/L4E11-SOURCE-ONLY-AND-ENTRY.md" -->
> **SELECTED (SESSION): (E)**, U42 TPS16630PWPR on board A between VBAT and a new net VSYS_DOCK on J_DOCK pin 1; R228 11.0 kOhm
> 0.1 % on ILIM (I(OL) = 18 / R(ILIM), Equation 6, p.20), C237 22 nF on dVdT, MODE and OVP to GND, UVLO and P_IN on IN, SHDN,
> IMON, FLT and PGOOD open (drafted in `apply_gen_sch_a_charger.py`; 17a adds C238, C239 and D23)
<!-- /q -->
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
