meshsat/meshsat-fieldkit/v2/release/review-packets/D-D12-1f614233/schematic/pcb-d-aprs-schematic-sheet.pdf

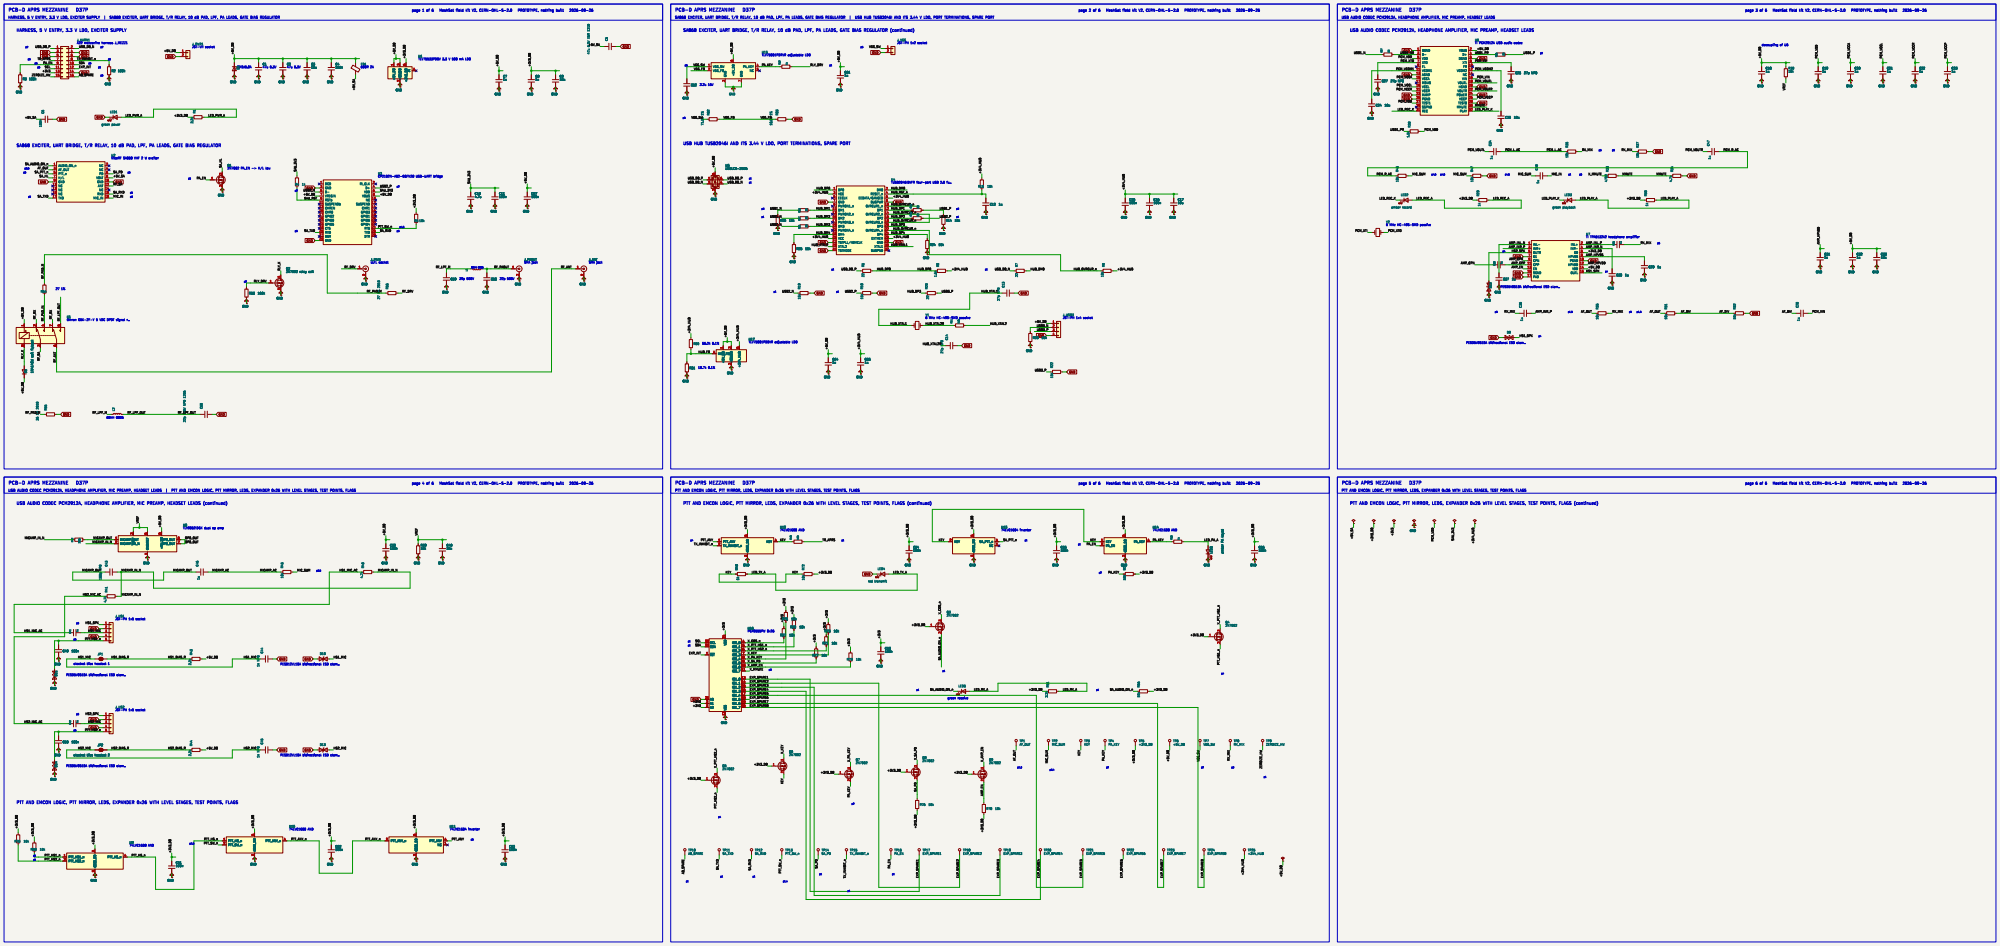
[picture p226: page 1]

USB AUDIO CODEC PCM2912A, HEADPHONE AMPLIFIER, MIC PREAMP, HEADSET LEADS

SA868 EXCITER, UART BRIDGE, T/R RELAY, 10 dB PAD, LPF, PA LEADS, GATE BIAS REGULATOR (continued)

56.2k 0.1% USB HUB TUSB2046I AND ITS 3.44 V LDO, PORT TERMINATIONS, SPARE PORT

p5 SA868 EXCITER, UART BRIDGE, T/R RELAY, 10 dB PAD, LPF, PA LEADS, GATE BIAS REGULATOR

PTT AND EMCON LOGIC, PTT MIRROR, LEDS, EXPANDER 0x26 WITH LEVEL STAGES, TEST POINTS, FLAGS

USB AUDIO CODEC PCM2912A, HEADPHONE AMPLIFIER, MIC PREAMP, HEADSET LEADS (continued)

PTT AND EMCON LOGIC, PTT MIRROR, LEDS, EXPANDER 0x26 WITH LEVEL STAGES, TEST POINTS, FLAGS (continued)
