meshsat/meshsat-fieldkit/v2/release/review-packets/E-E17-1f614233/schematic/pcb-e1-dock-schematic-sheet.pdf

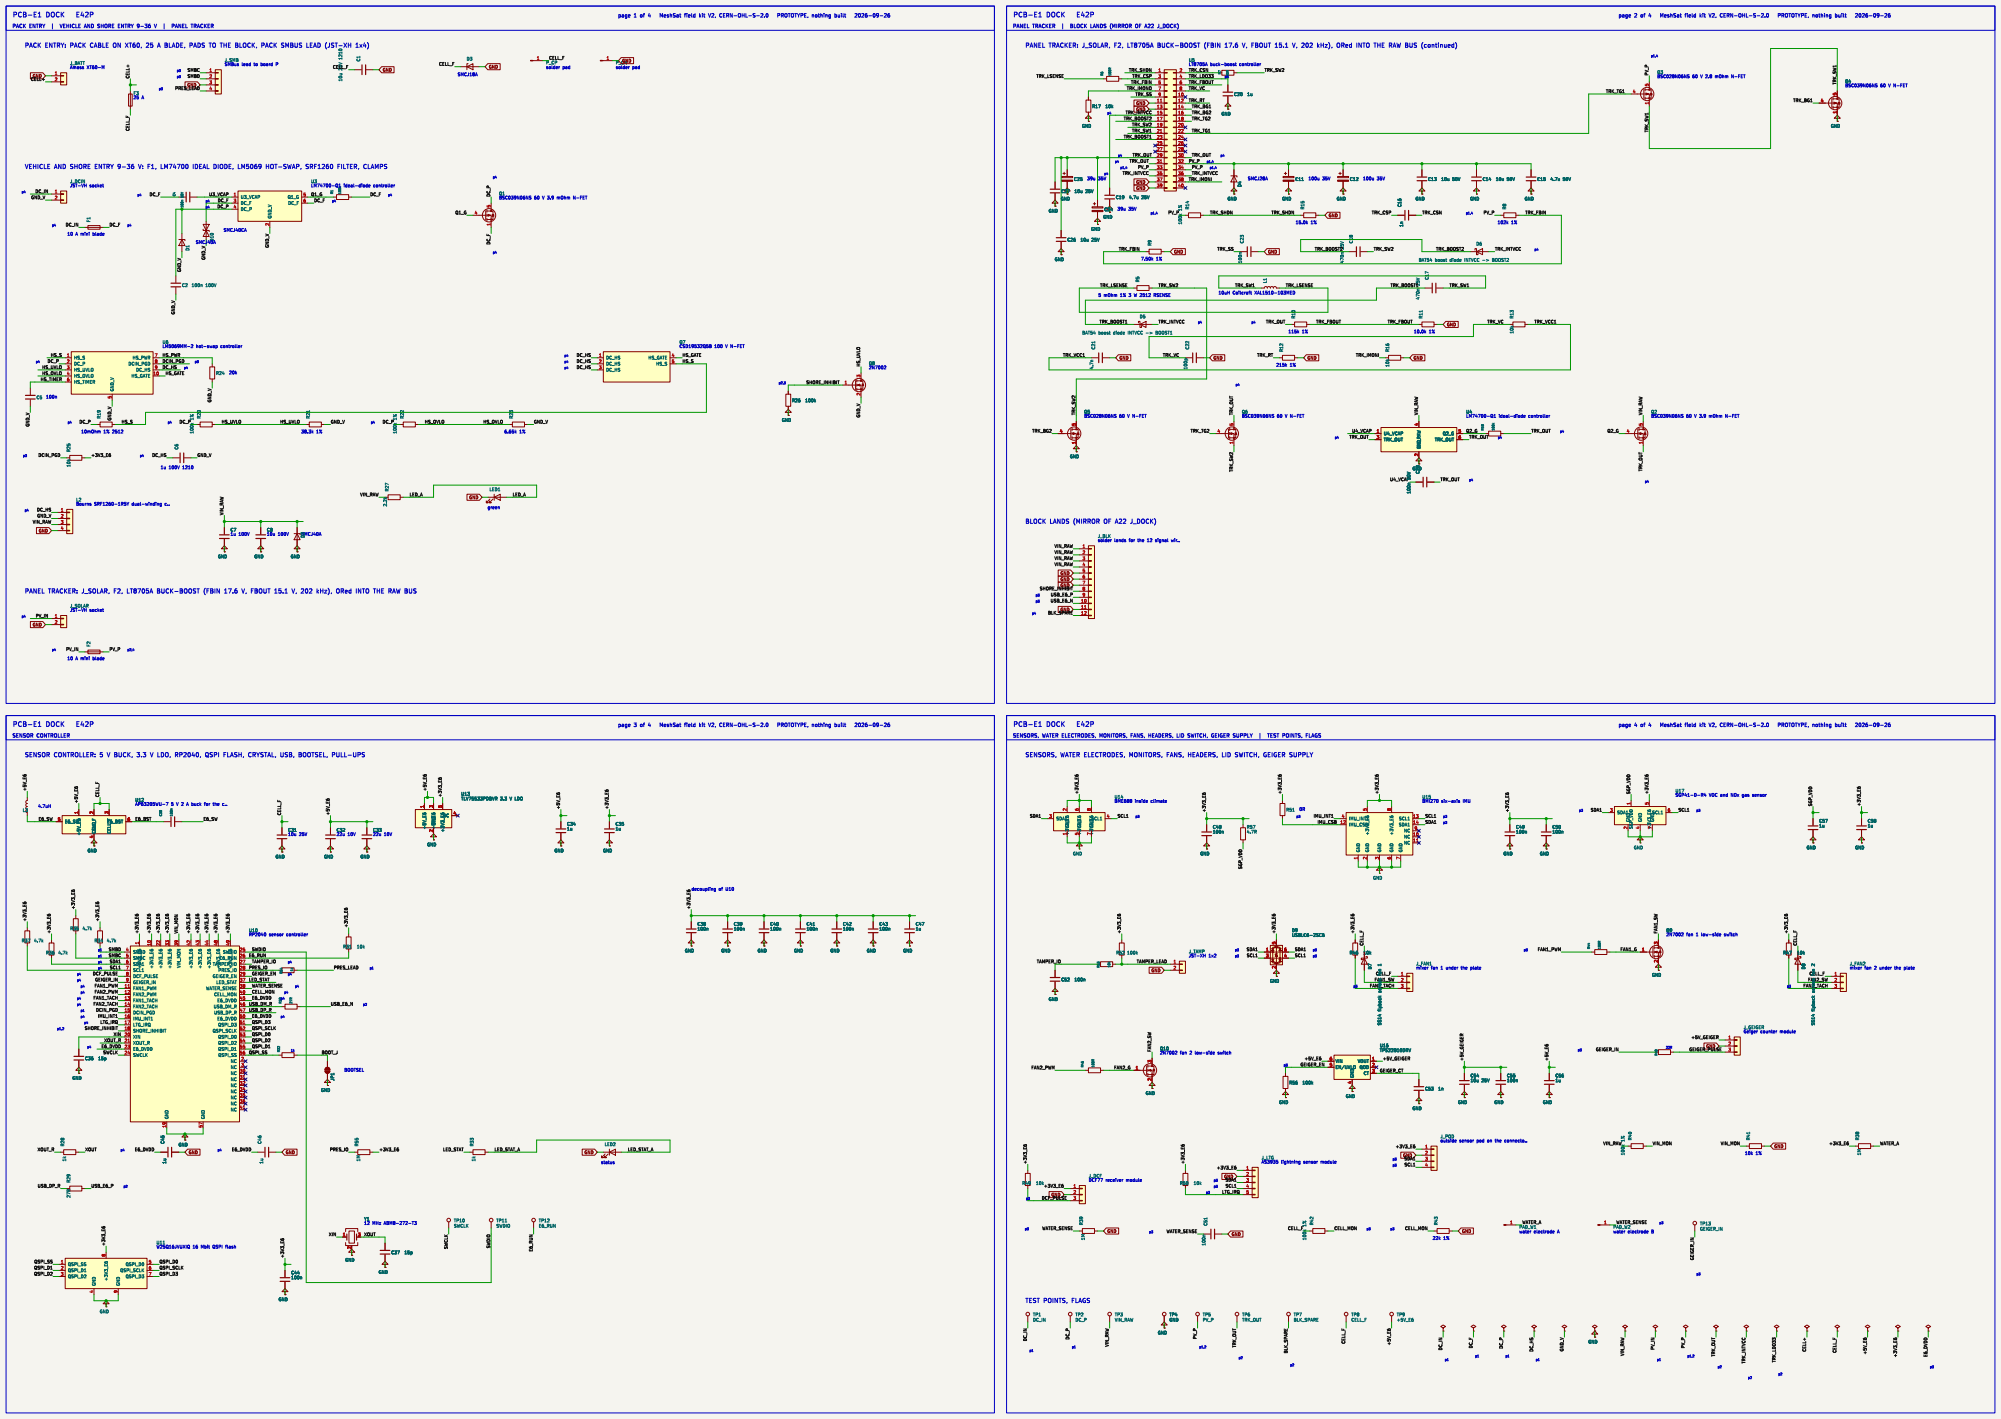
[picture p227: page 1]
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

J_SMB
p1,4 SMBus lead to board P

5 1 Q6C23 100n R5 D5 BAT54 boost diode INTVCC -> BOOST1 GND R11 R16 10k C17 470n 25V C12 GND

p4 PANEL TRACKER: J_SOLAR, F2, LT8705A BUCK-BOOST (FBIN 17.6 V, FBOUT 15.1 V, 202 kHz), ORed INTO THE RAW BUS

SENSORS, WATER ELECTRODES, MONITORS, FANS, HEADERS, LID SWITCH, GEIGER SUPPLY

FAN2_SW +3V3_E6 +3V3_E6
LED_STAT 37 WATER_SENSE 38 CELL_MON 40 E6_DVDD 45 USB_DM_R 46 USB_DP_R 47 E6_DVDD 50 QSPI_D3 51 QSPI_SCLK 52 QSPI_D0 53 QSPI_D2 54 QSPI_D1 55 QSPI_SS 56 NC 2 NC 3 NC 30 NC 31 NC 32 NC 34 NC 35 NC 36 NC 41 U10

mixer fan 1 under the plate

J_POD
outside sensor pod on the connecto..
