meshsat/meshsat-fieldkit/v2/release/review-packets/P-P4-1f614233/schematic/pcb-p-pack-schematic-sheet.pdf

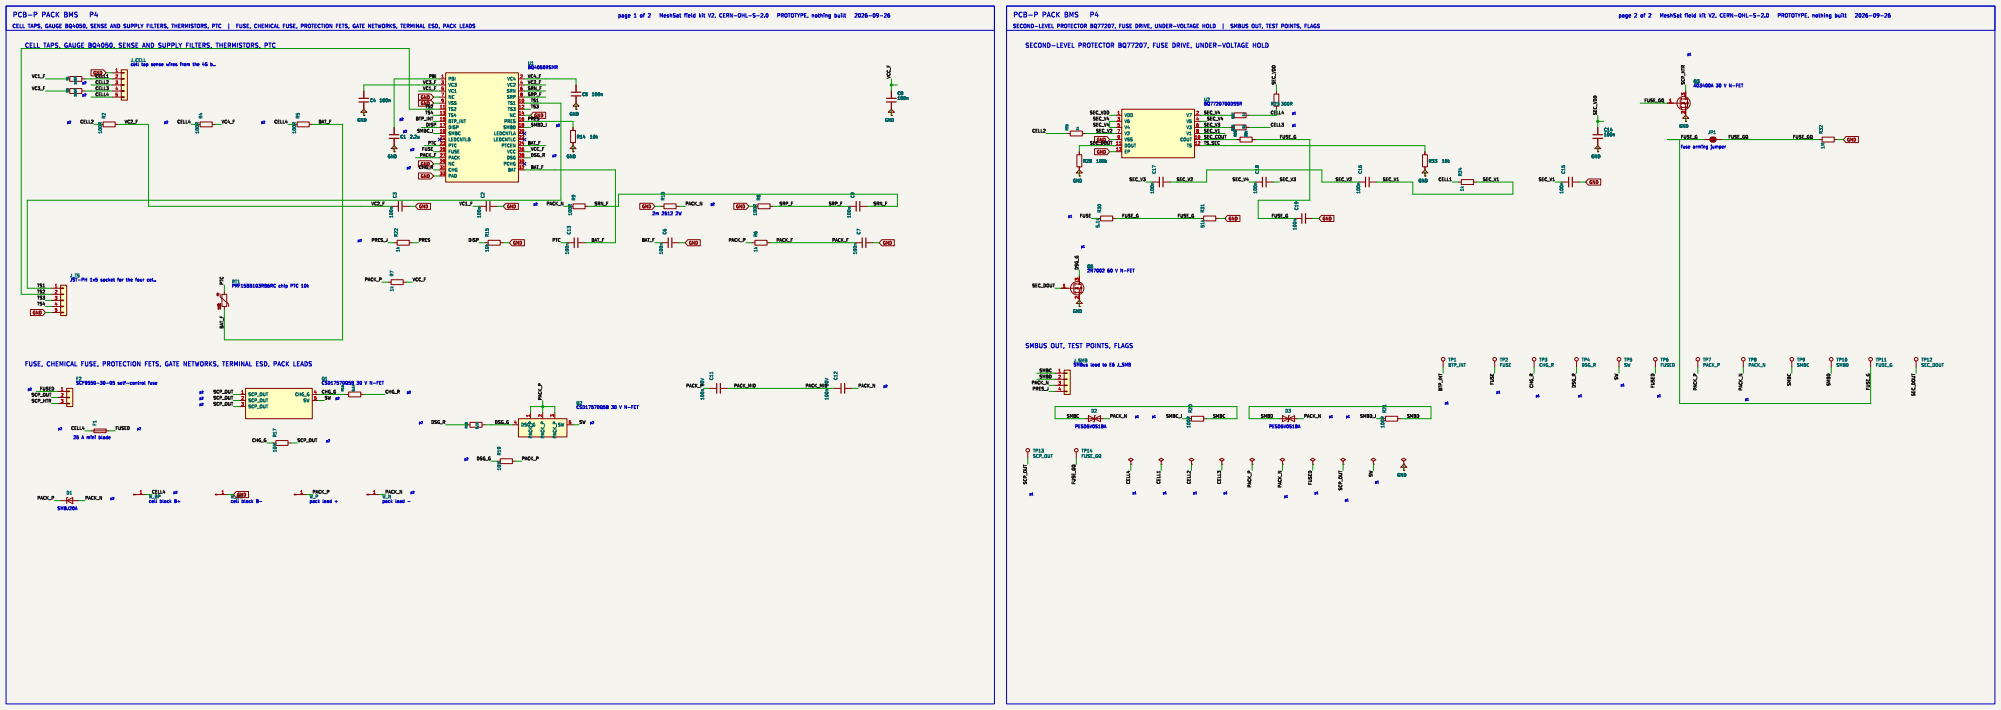
[picture p228: page 1]

CELL TAPS, GAUGE BQ4050, SENSE AND SUPPLY FILTERS, THERMISTORS, PTC

cell tap sense wires from the 4S b..

p2 FUSE, CHEMICAL FUSE, PROTECTION FETS, GATE NETWORKS, TERMINAL ESD, PACK LEADS
