meshsat/meshsat-fieldkit/v2/release/revA/boards/meshsat-pcb-c-revA-C24/pcb-c-display-schematic.pdf

D15 | +5V
USB_PNL_P USB_PNL_N | +3V³ EPD_RESE

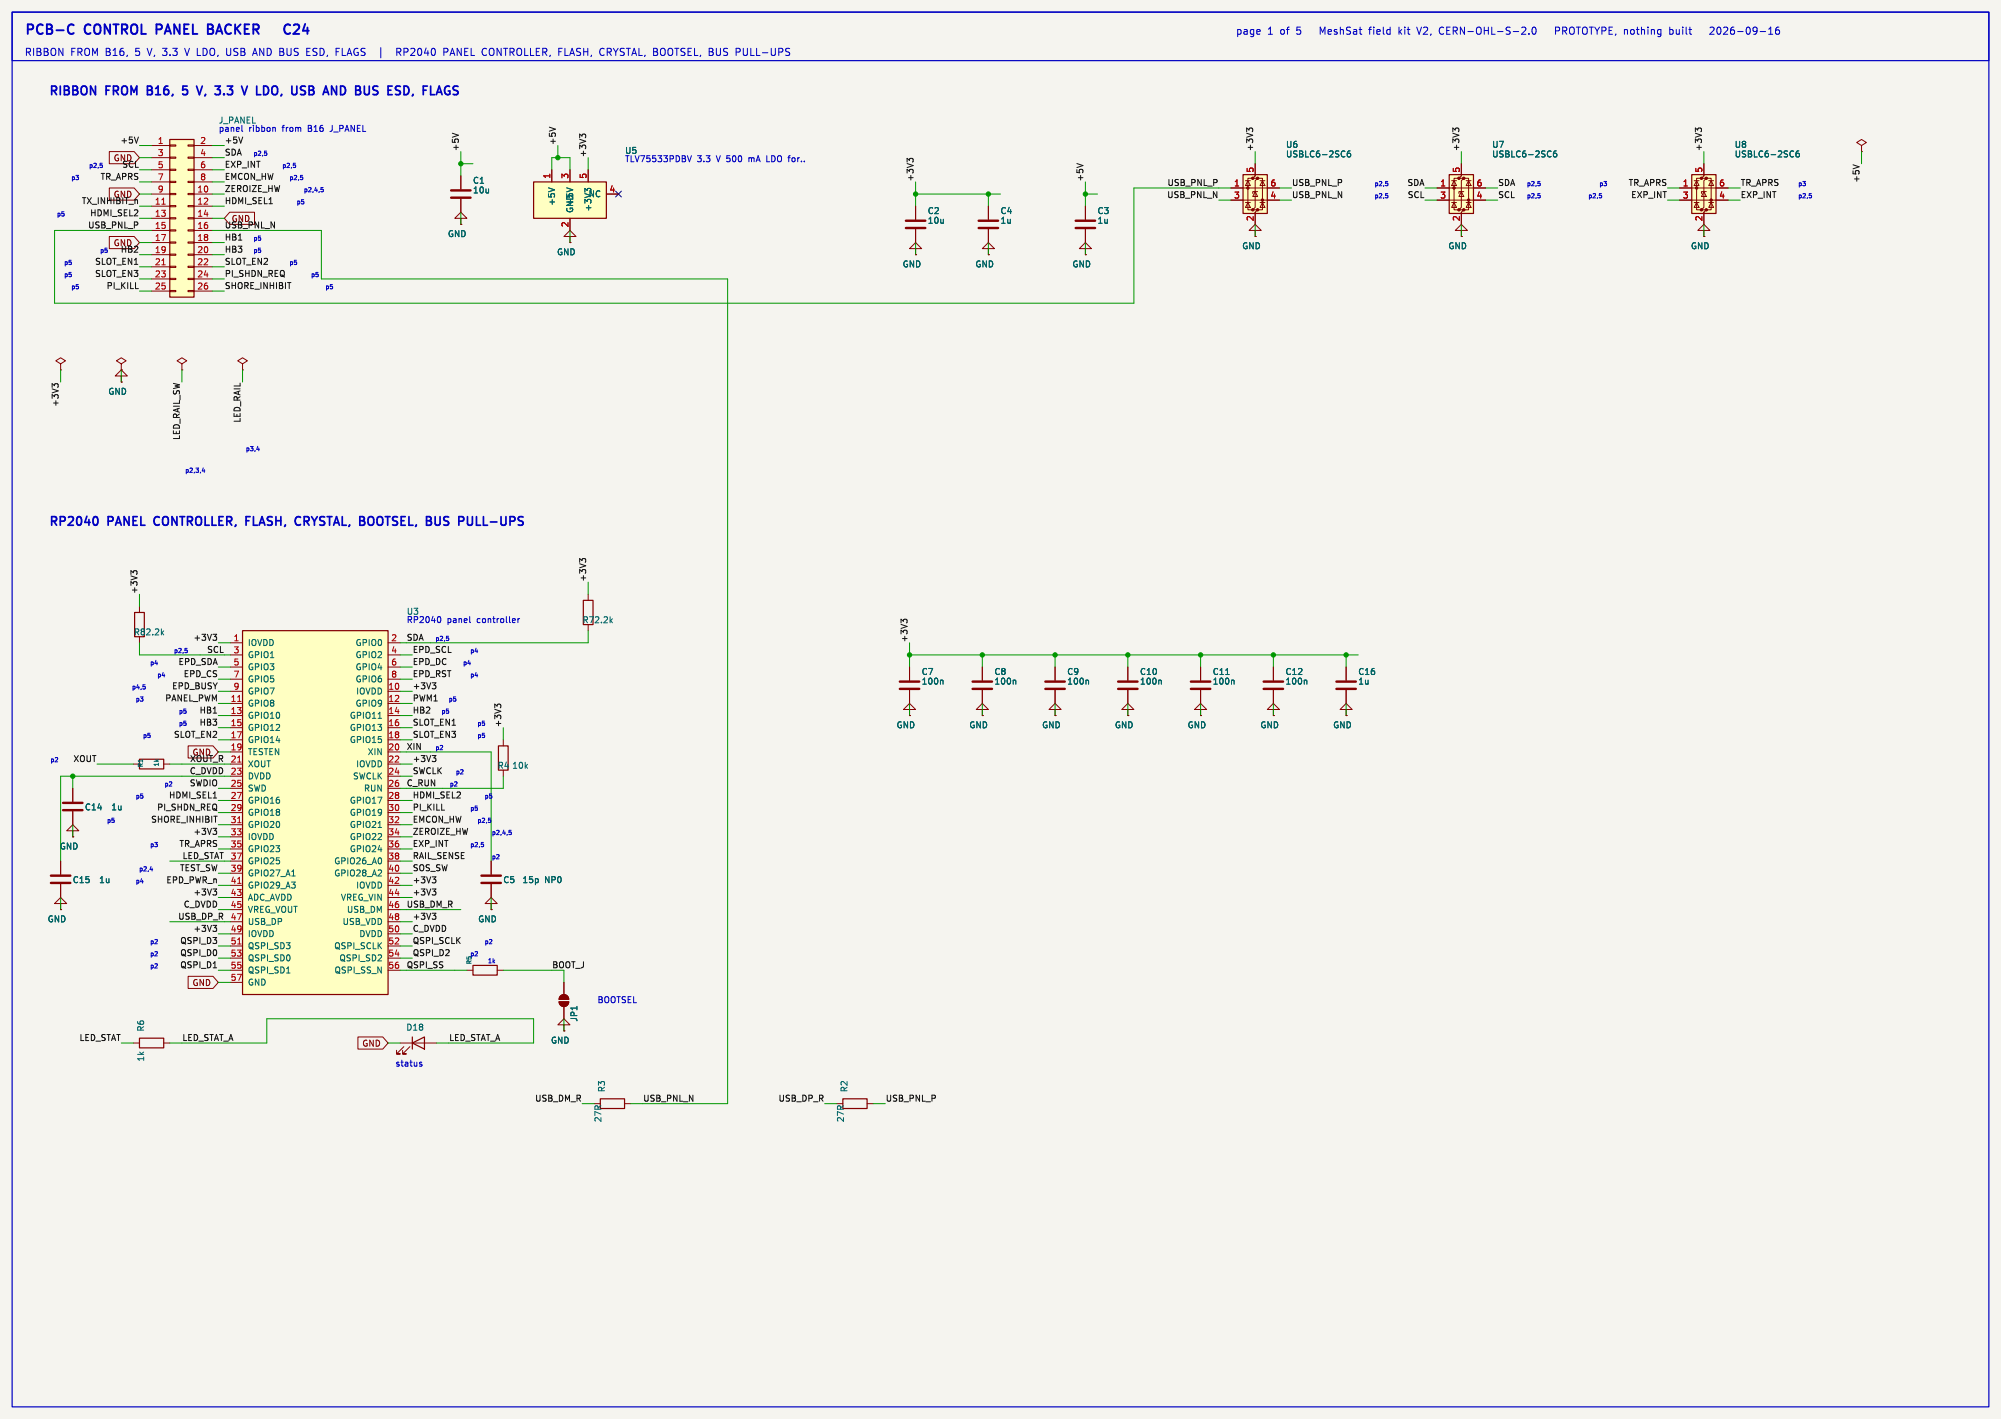
[picture p229: page 1]

RIBBON FROM B16, 5 V, 3.3 V LDO, USB AND BUS ESD, FLAGS

RP2040 PANEL CONTROLLER, FLASH, CRYSTAL, BOOTSEL, BUS PULL-UPS

IOVDD 1 GPIO1 3 GPIO3 5 GPIO5 7 GPIO7 9 GPIO8 11 GPIO10 13 GPIO12 15 GPIO14 17 TESTEN 19 XOUT 21 DVDD 23 SWD 25 GPIO16 27 GPIO18 29 GPIO20 31

7 U4

## p1 LED RAIL, INDICATORS, TX LAMP, SWITCHES AND LEADS

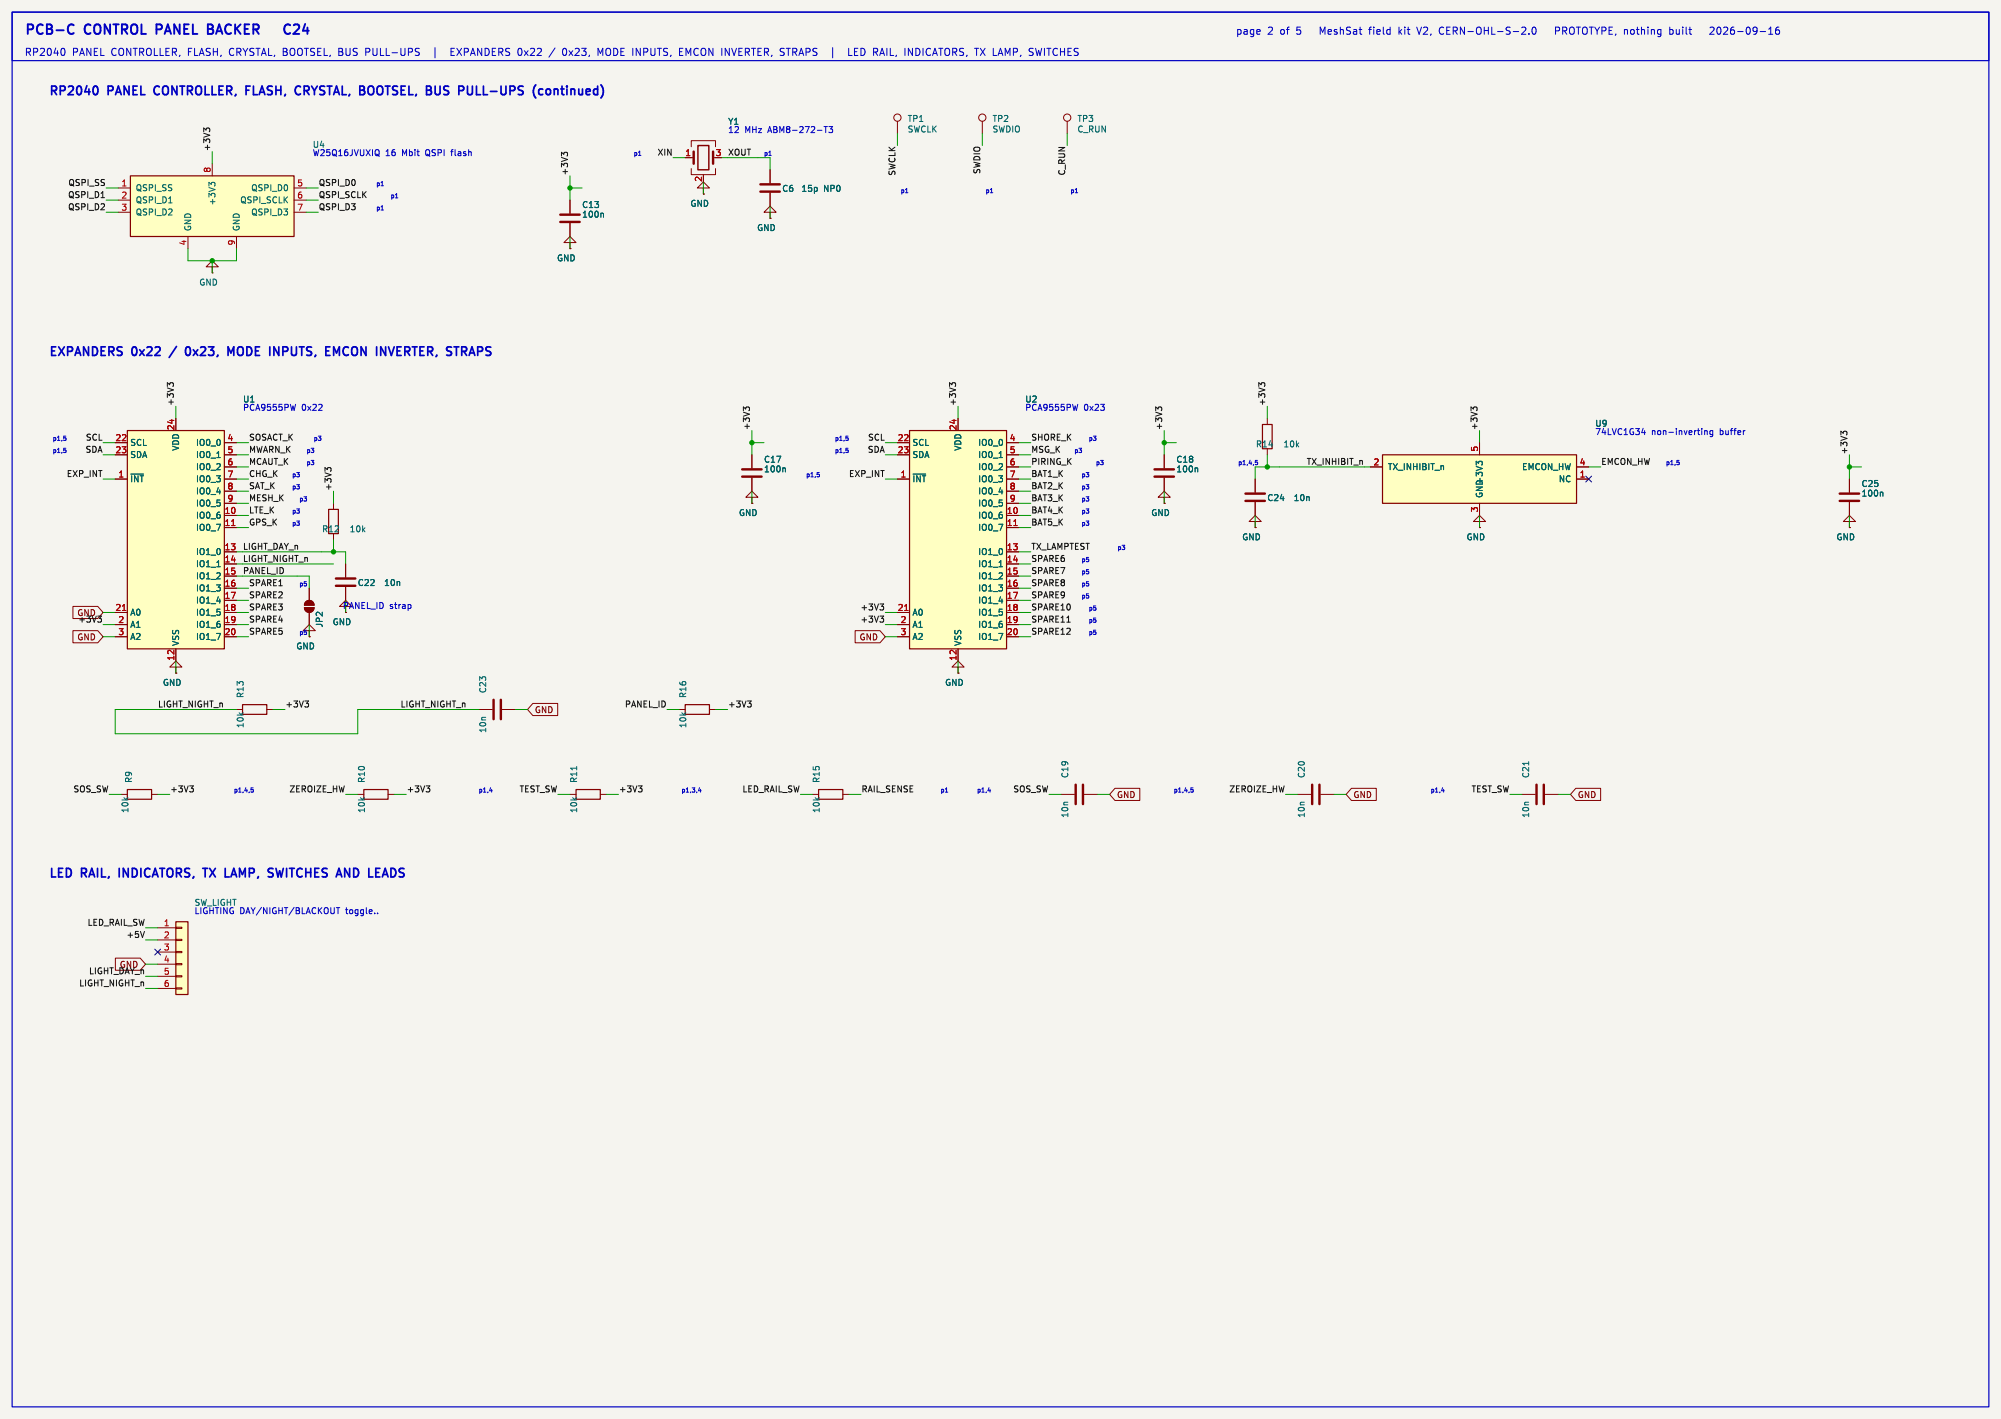
[picture p230: page 2]

D15 | +5V
H4 TP39 PIJ2_A | R¹³ 10k GND | GND R⁹ 10k | R¹⁰ 10k

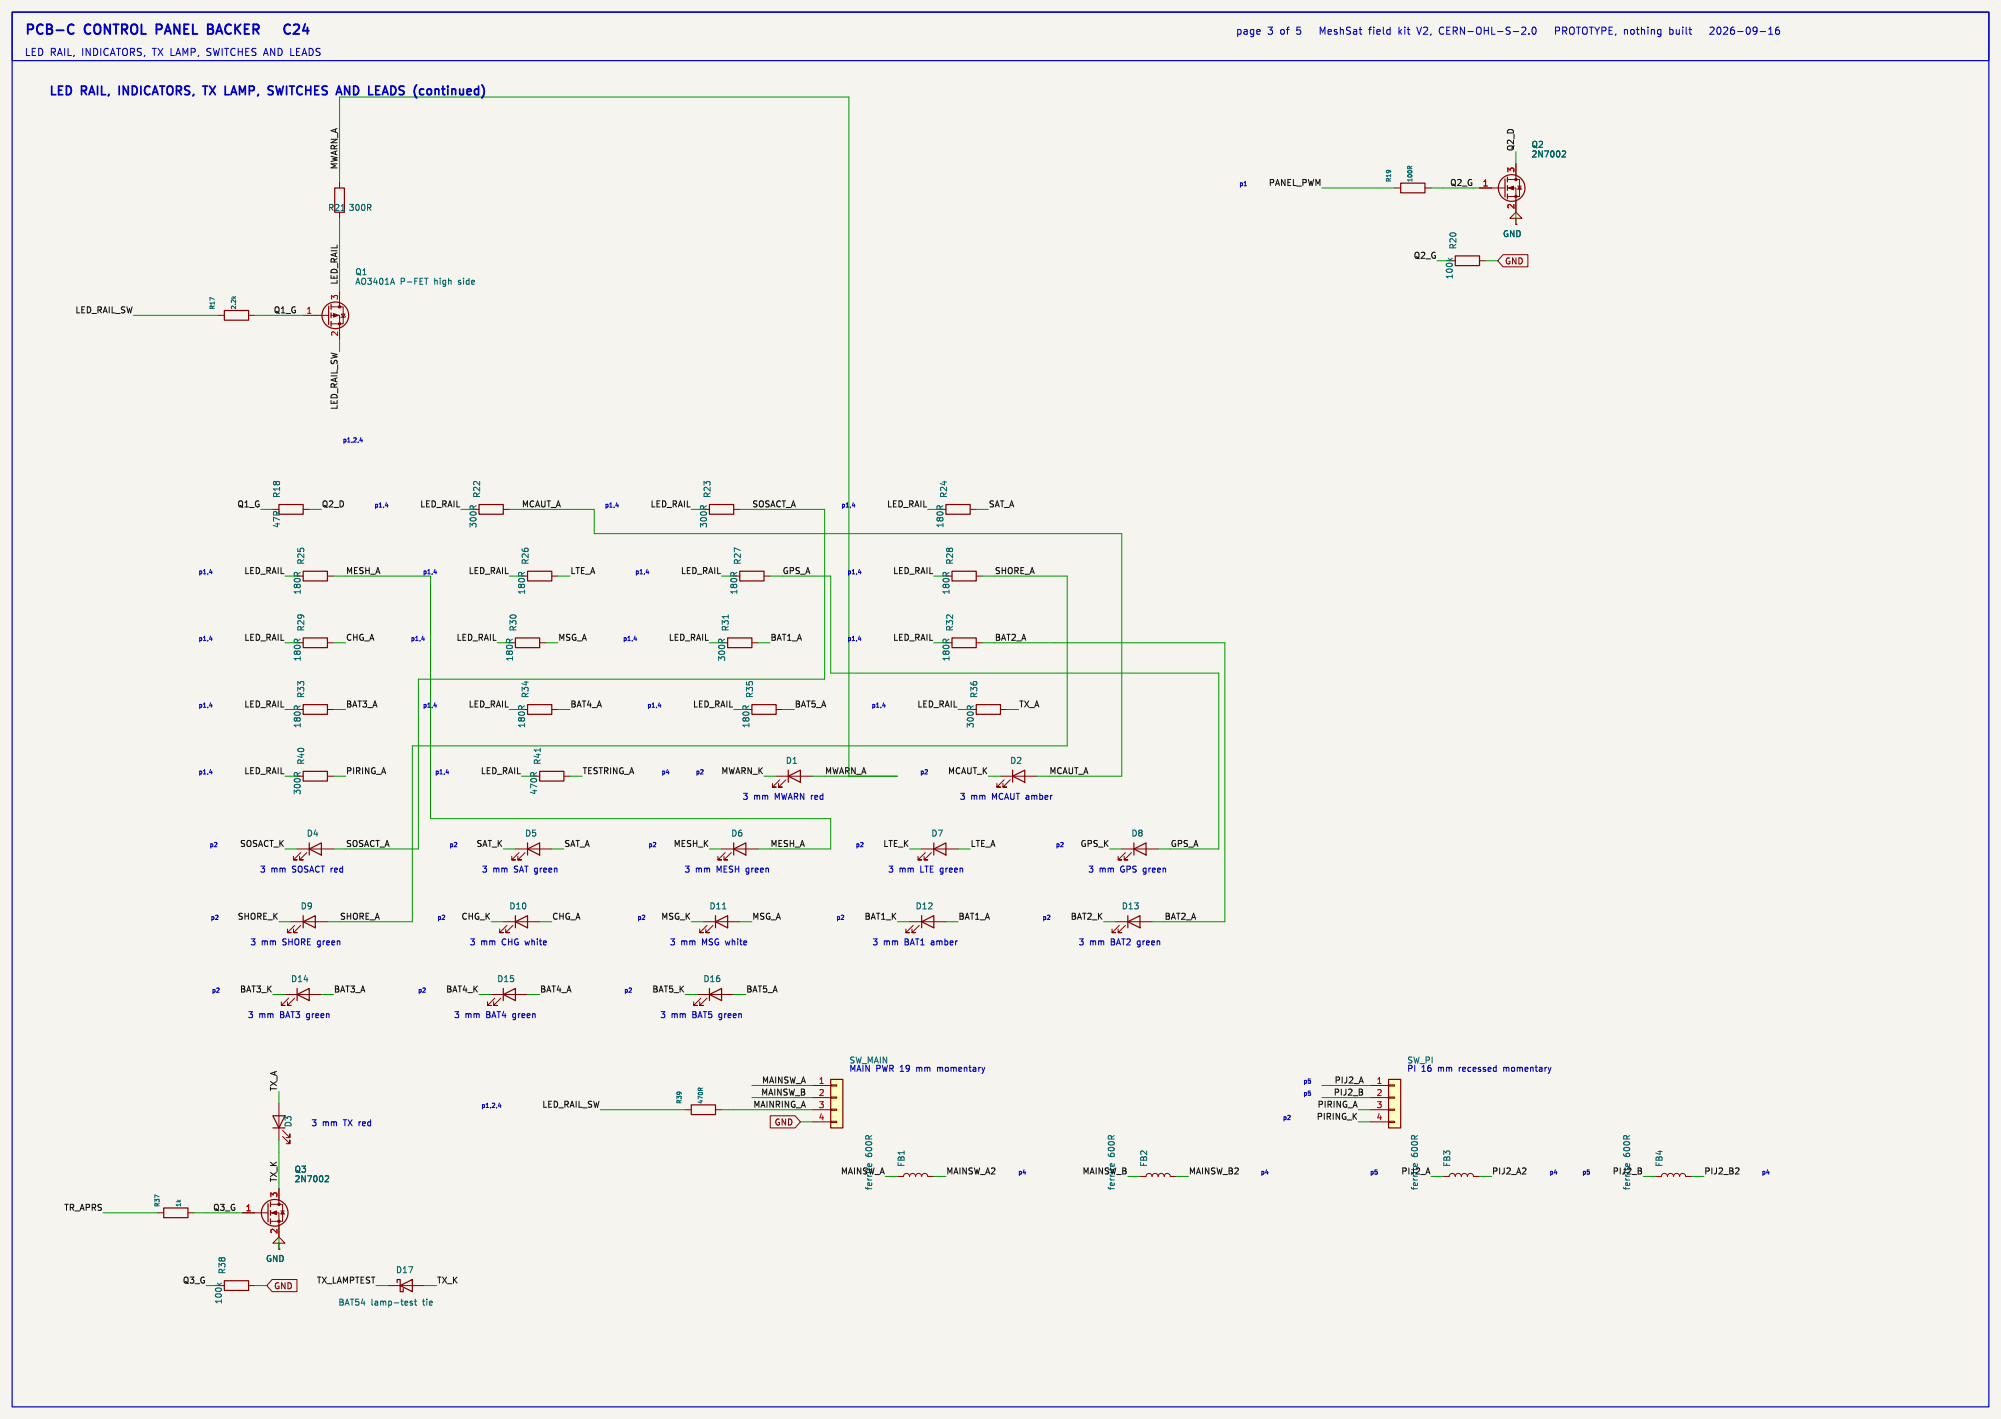
[picture p231: page 3]

LED RAIL, INDICATORS, TX LAMP, SWITCHES AND LEADS
PIRING_A LED_RAIL EPD_SW
LED_RAIL MCAUT_A

LED RAIL, INDICATORS, TX LAMP, SWITCHES AND LEADS (continued)

PI 16 mm recessed momentary

H4 TP39 PIJ2_A | R¹³ 10k GND | GND R⁹ 10k | R¹⁰ 10k
GND | GND

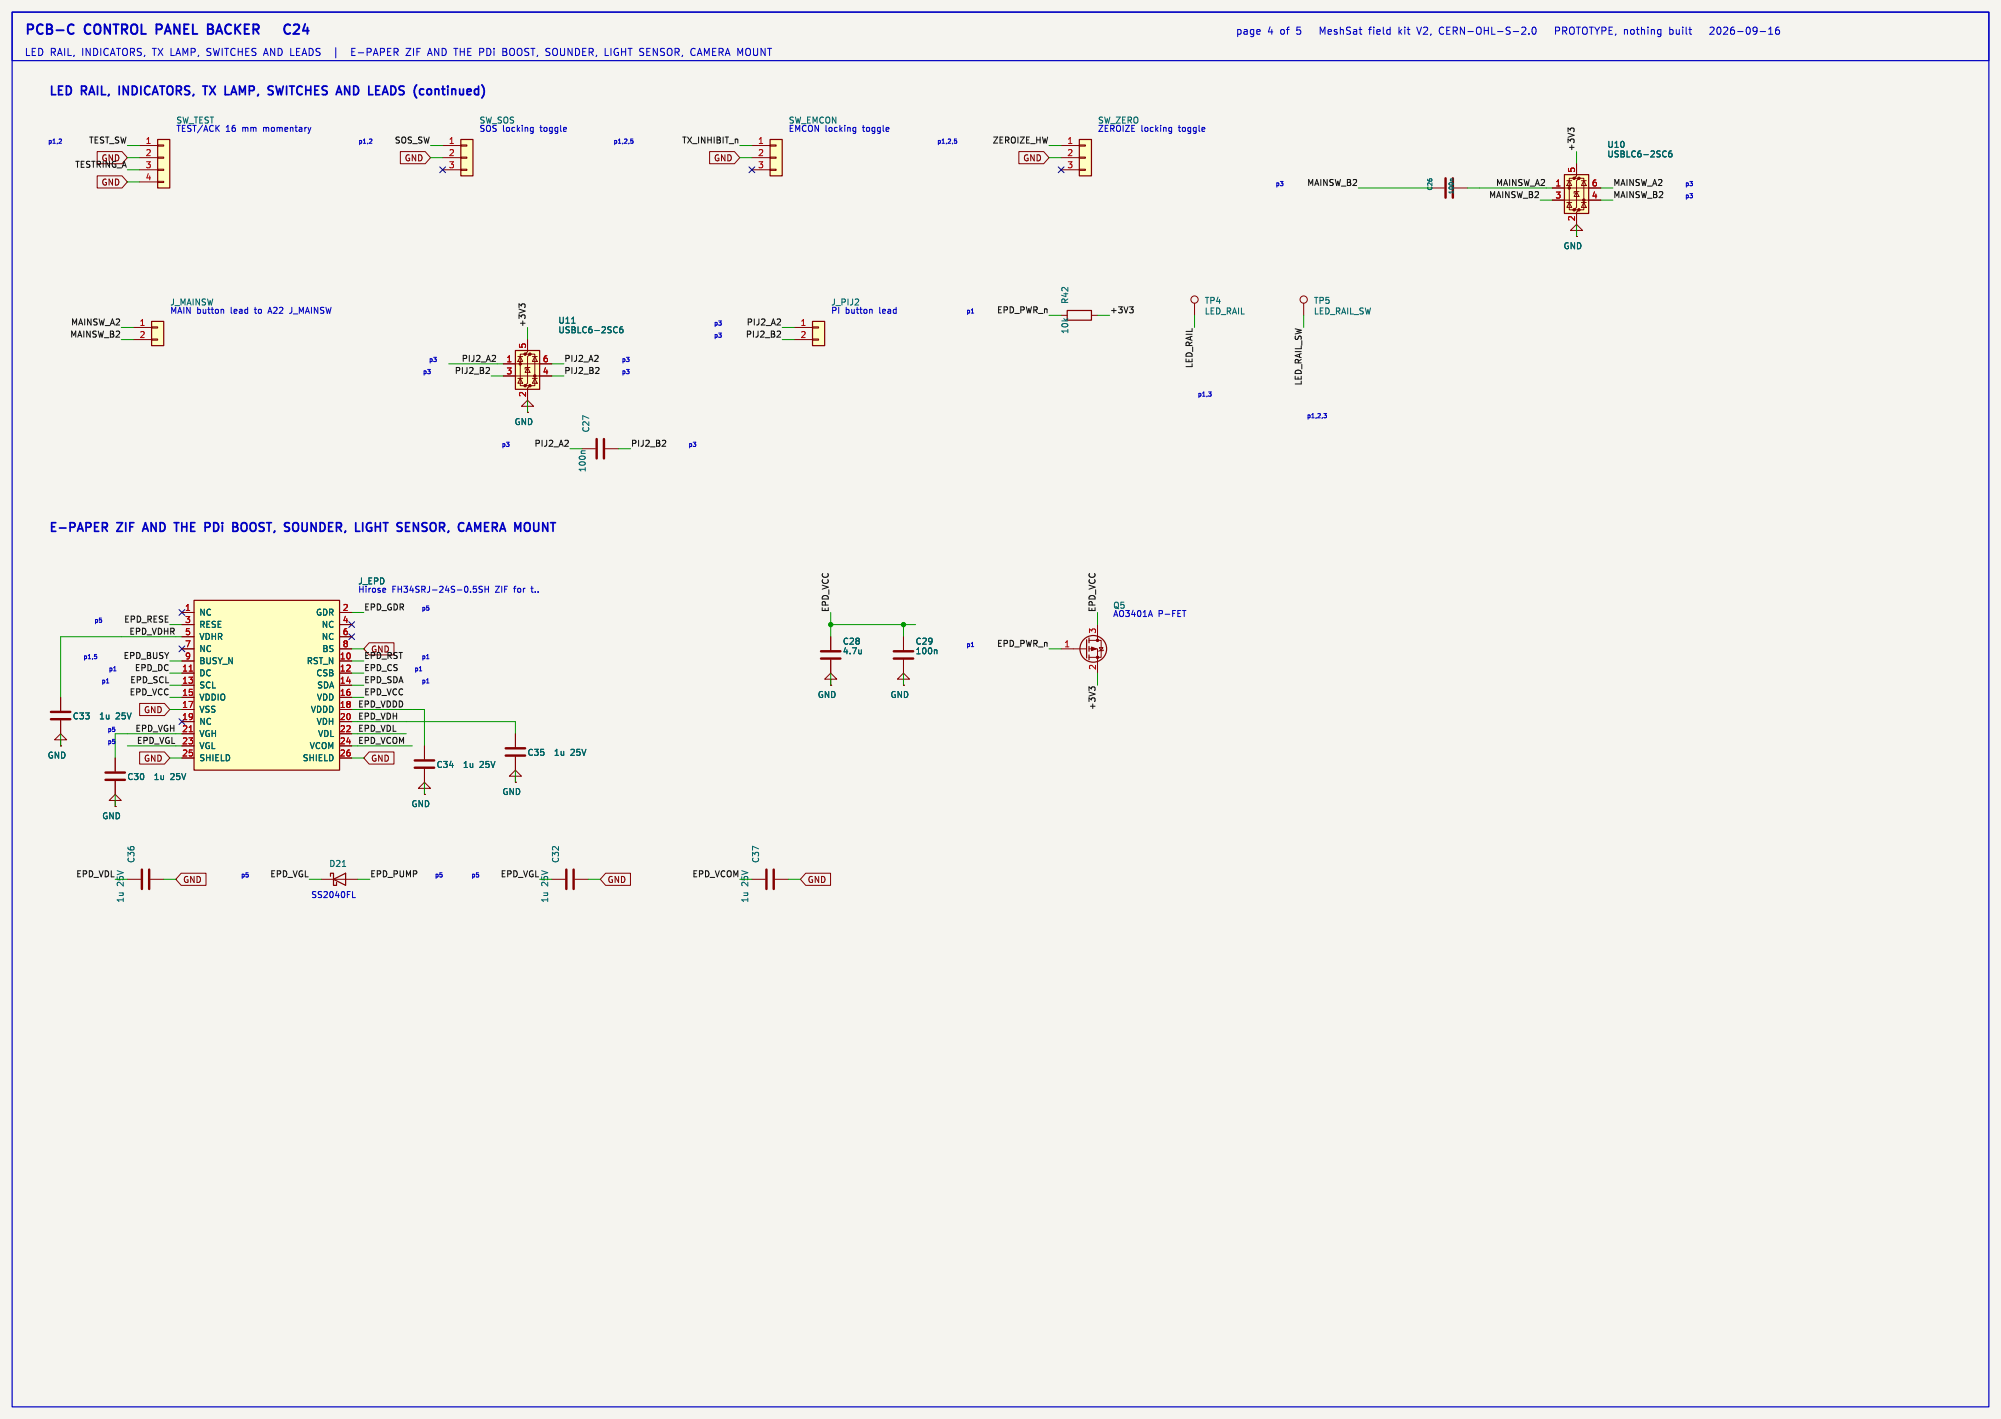
[picture p232: page 4]

p1,2 LED RAIL, INDICATORS, TX LAMP, SWITCHES AND LEADS (continued)

TEST/ACK 16 mm momentary

J_MAINSW
MAIN button lead to A22 J_MAINSW

E-PAPER ZIF AND THE PDi BOOST, SOUNDER, LIGHT SENSOR, CAMERA MOUNT

H4 TP39 PIJ2_A | R¹³ 10k GND | GND R⁹ 10k | R¹⁰ 10k
TP21 SPARE9 TP20 SPARE8 TP17 SPARE5 | R³⁵ 180R

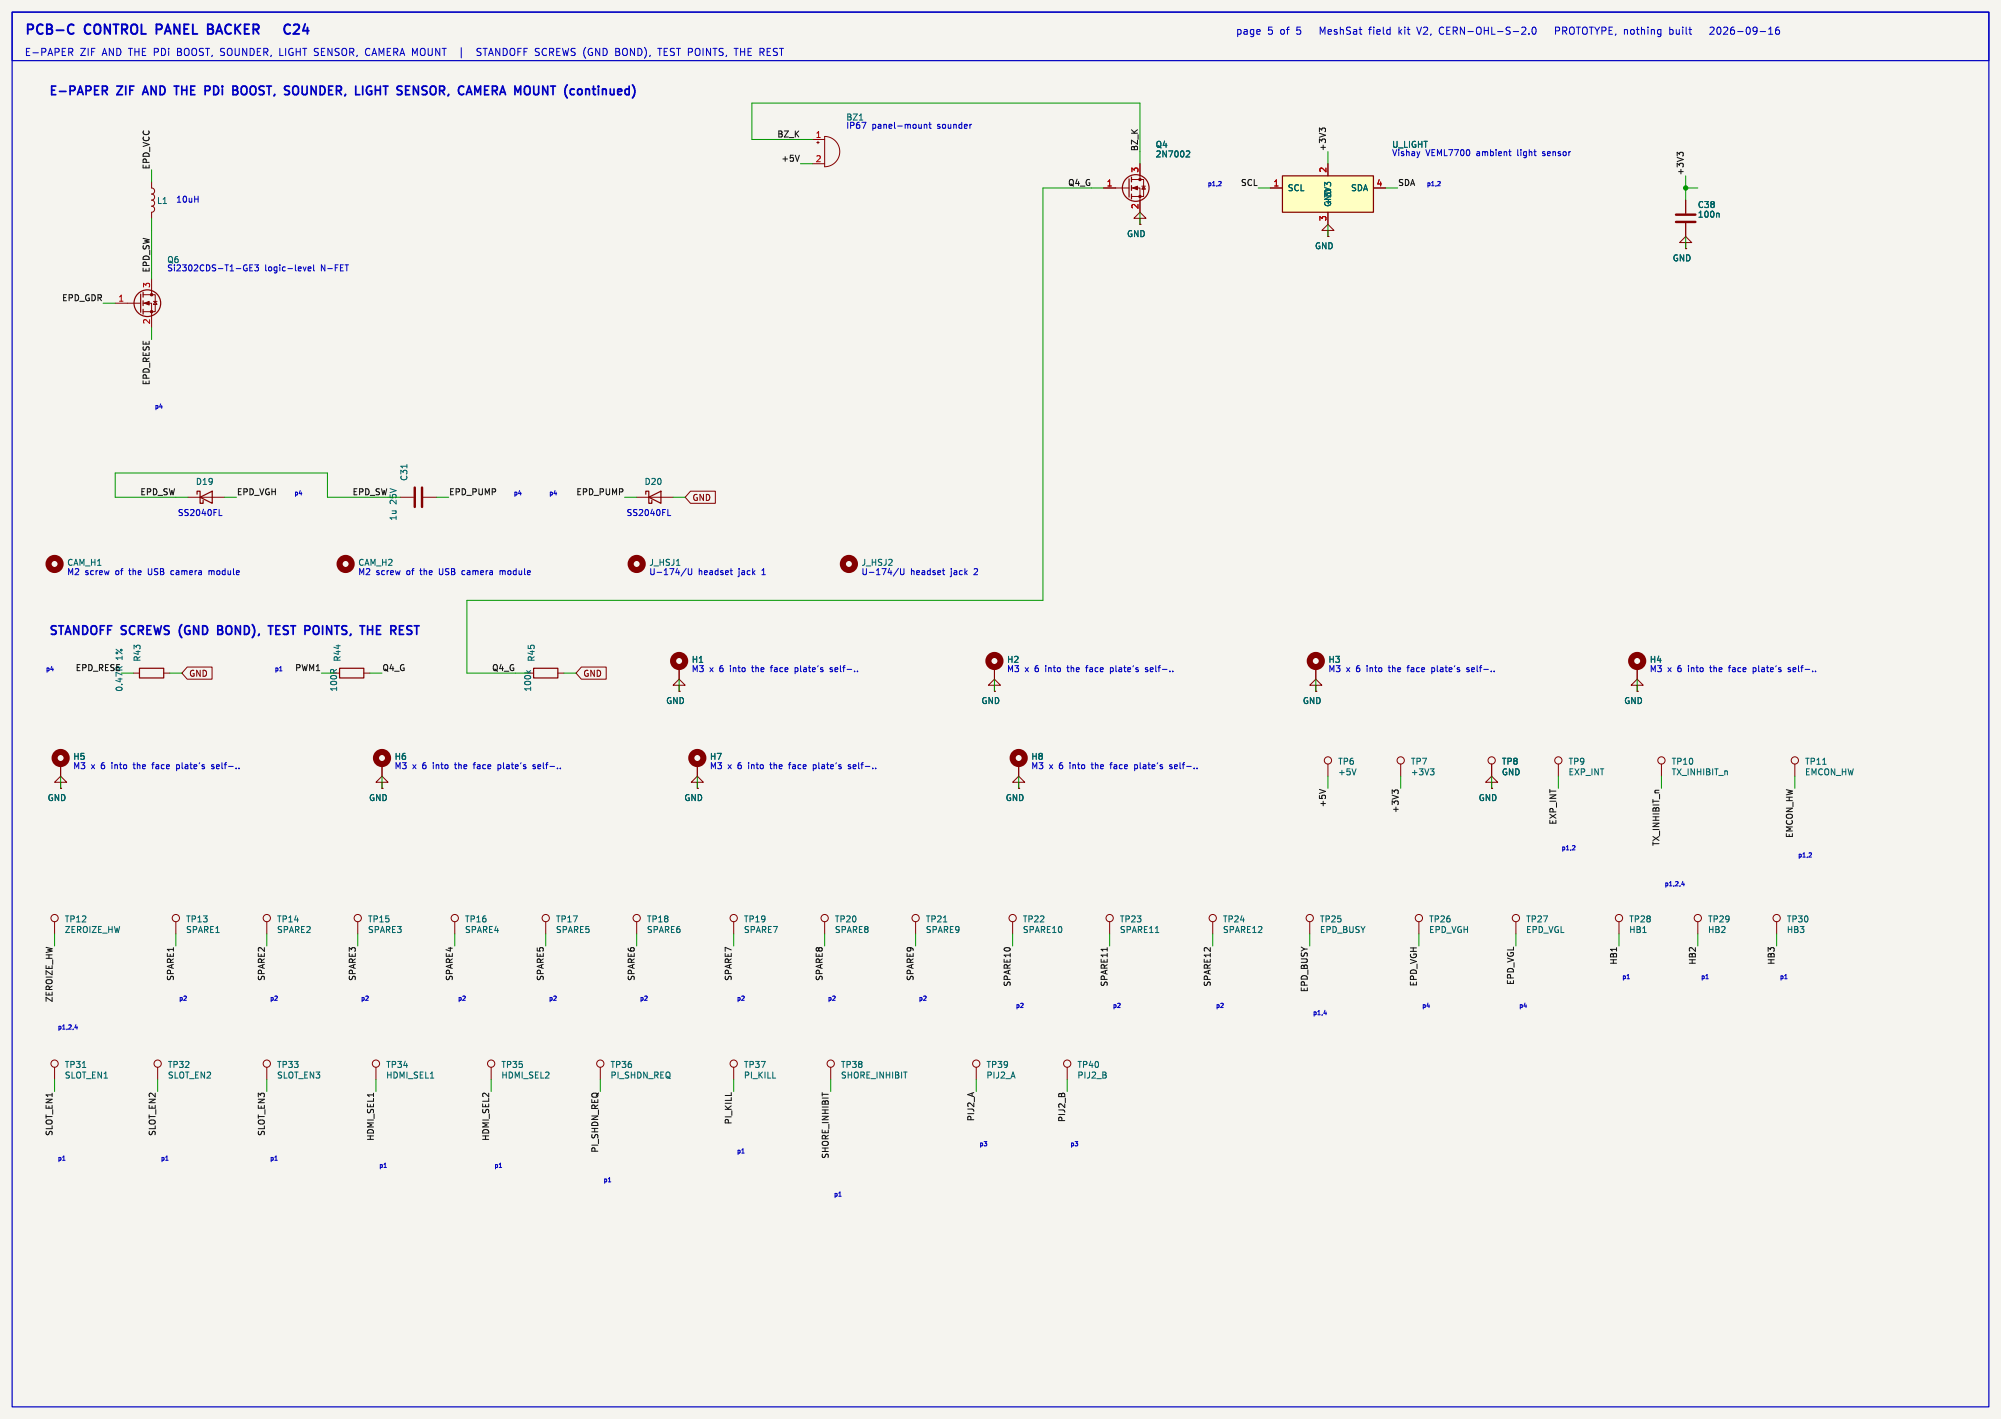
[picture p233: page 5]

Vishay VEML7700 ambient light sensor p4

CAM_H1
M2 screw of the USB camera module

CAM_H2

STANDOFF SCREWS (GND BOND), TEST POINTS, THE REST
