meshsat/meshsat-fieldkit/v2/release/revA/boards/meshsat-pcb-d-revA-D11/pcb-d-aprs-schematic.pdf

# 100n C⁵ 47u 6.3V X⁵R ¹²¹⁰

# 2N7002 D¹ SMBJ5.0A

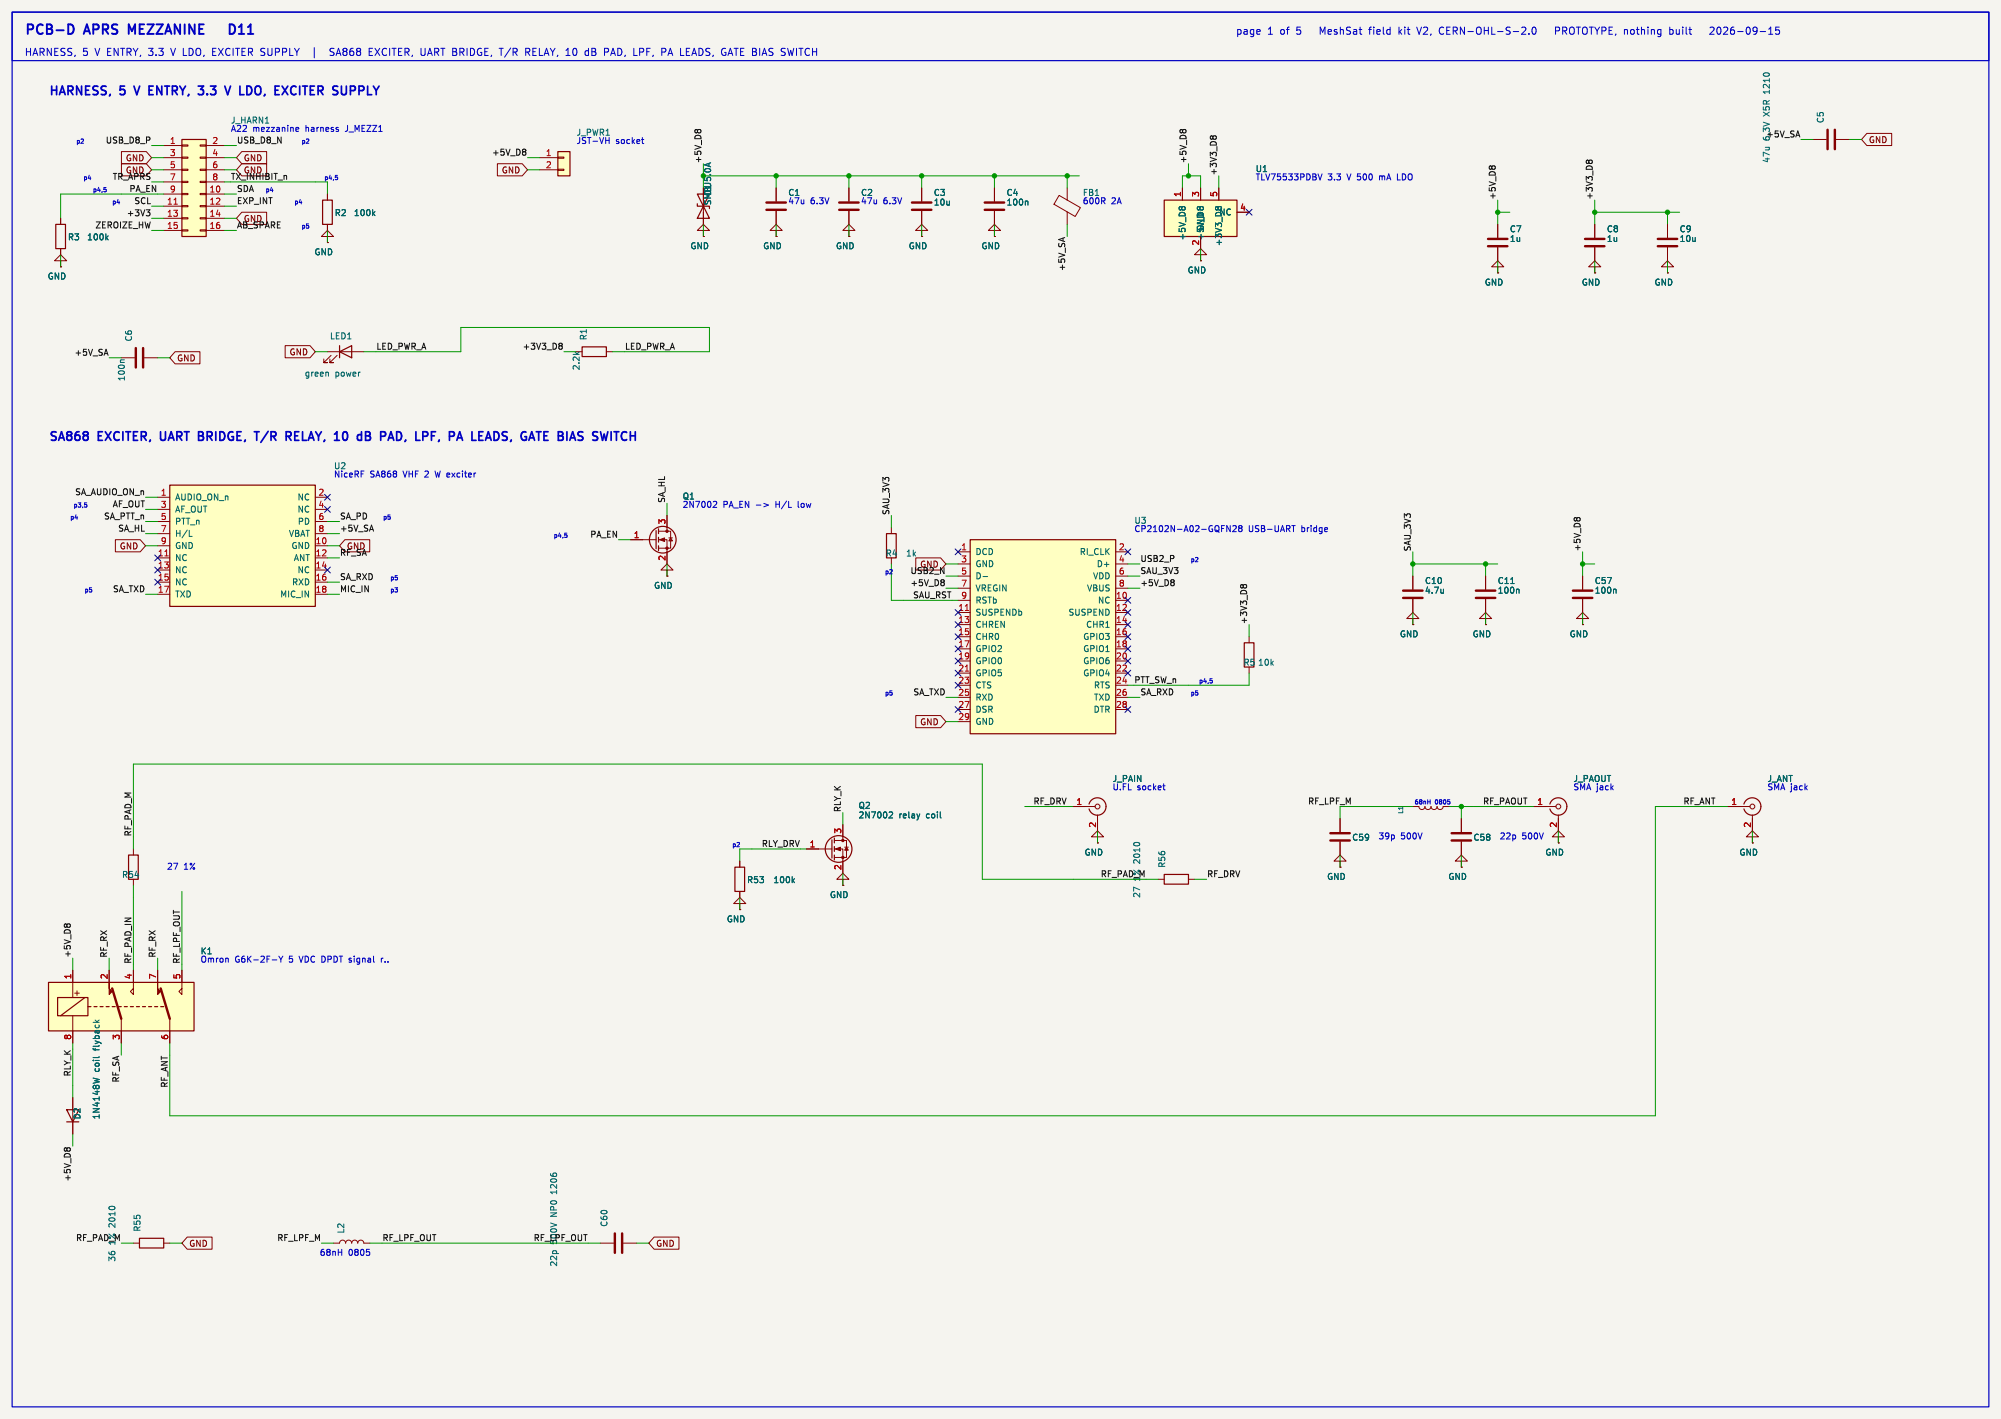
[picture p234: page 1]

HARNESS, 5 V ENTRY, 3.3 V LDO, EXCITER SUPPLY

SA868 EXCITER, UART BRIDGE, T/R RELAY, 10 dB PAD, LPF, PA LEADS, GATE BIAS SWITCH

# 100n C⁵ 47u 6.3V X⁵R ¹²¹⁰

3 U15 TPS22810DRV GND R¹⁹ 15k R¹¹ | 1.5k | 1

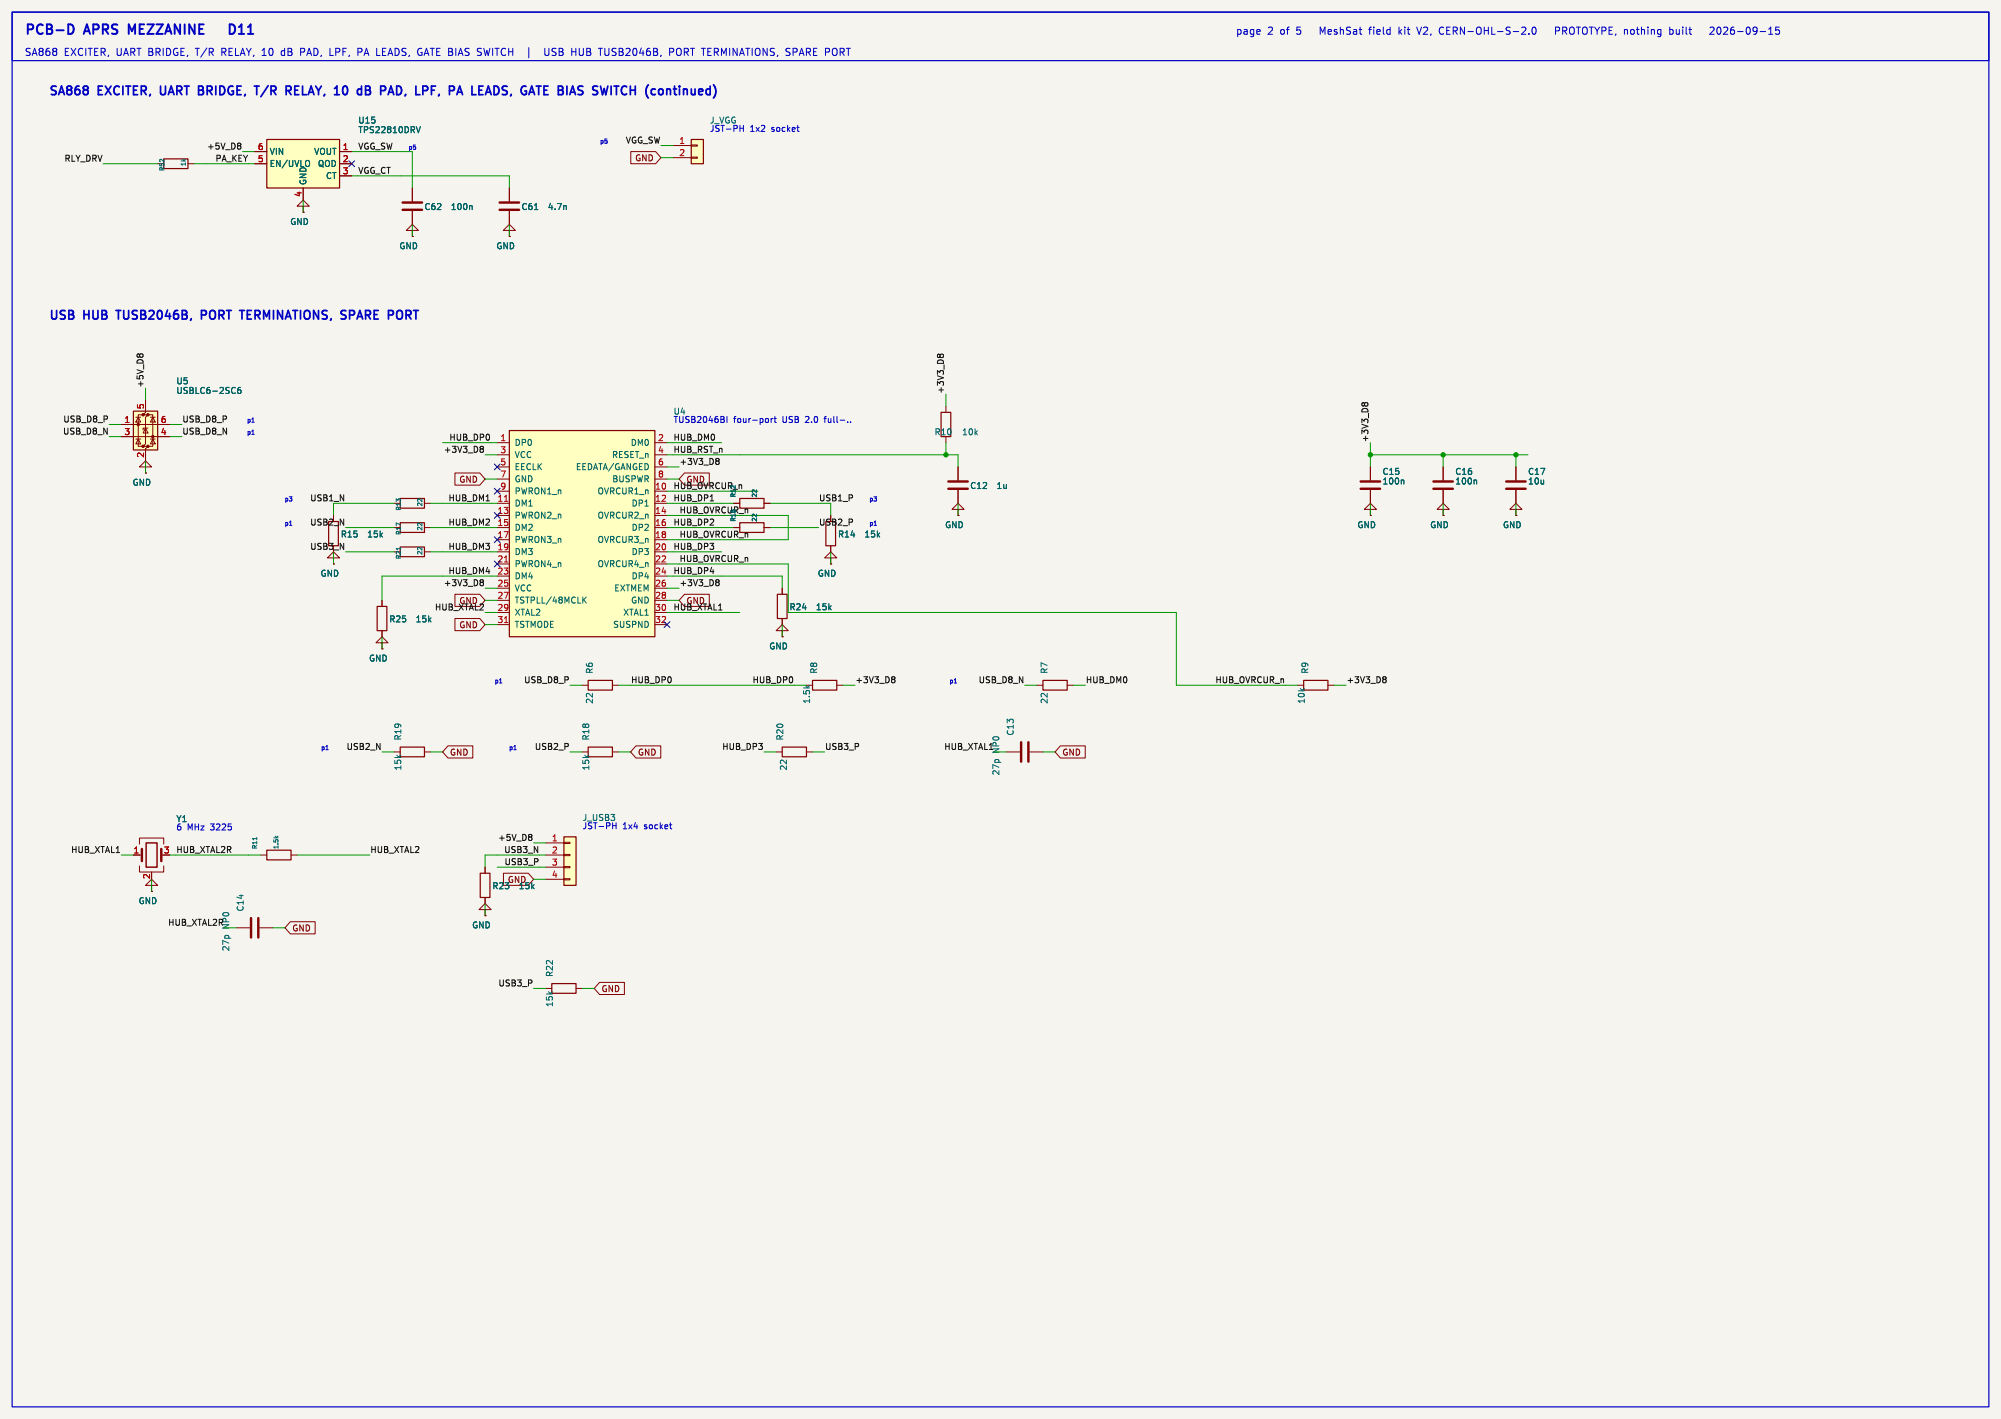
[picture p235: page 2]

p1 USB HUB TUSB2046B, PORT TERMINATIONS, SPARE PORT

# 100n C⁵ 47u 6.3V X⁵R ¹²¹⁰

# 2N7002 D¹ SMBJ5.0A

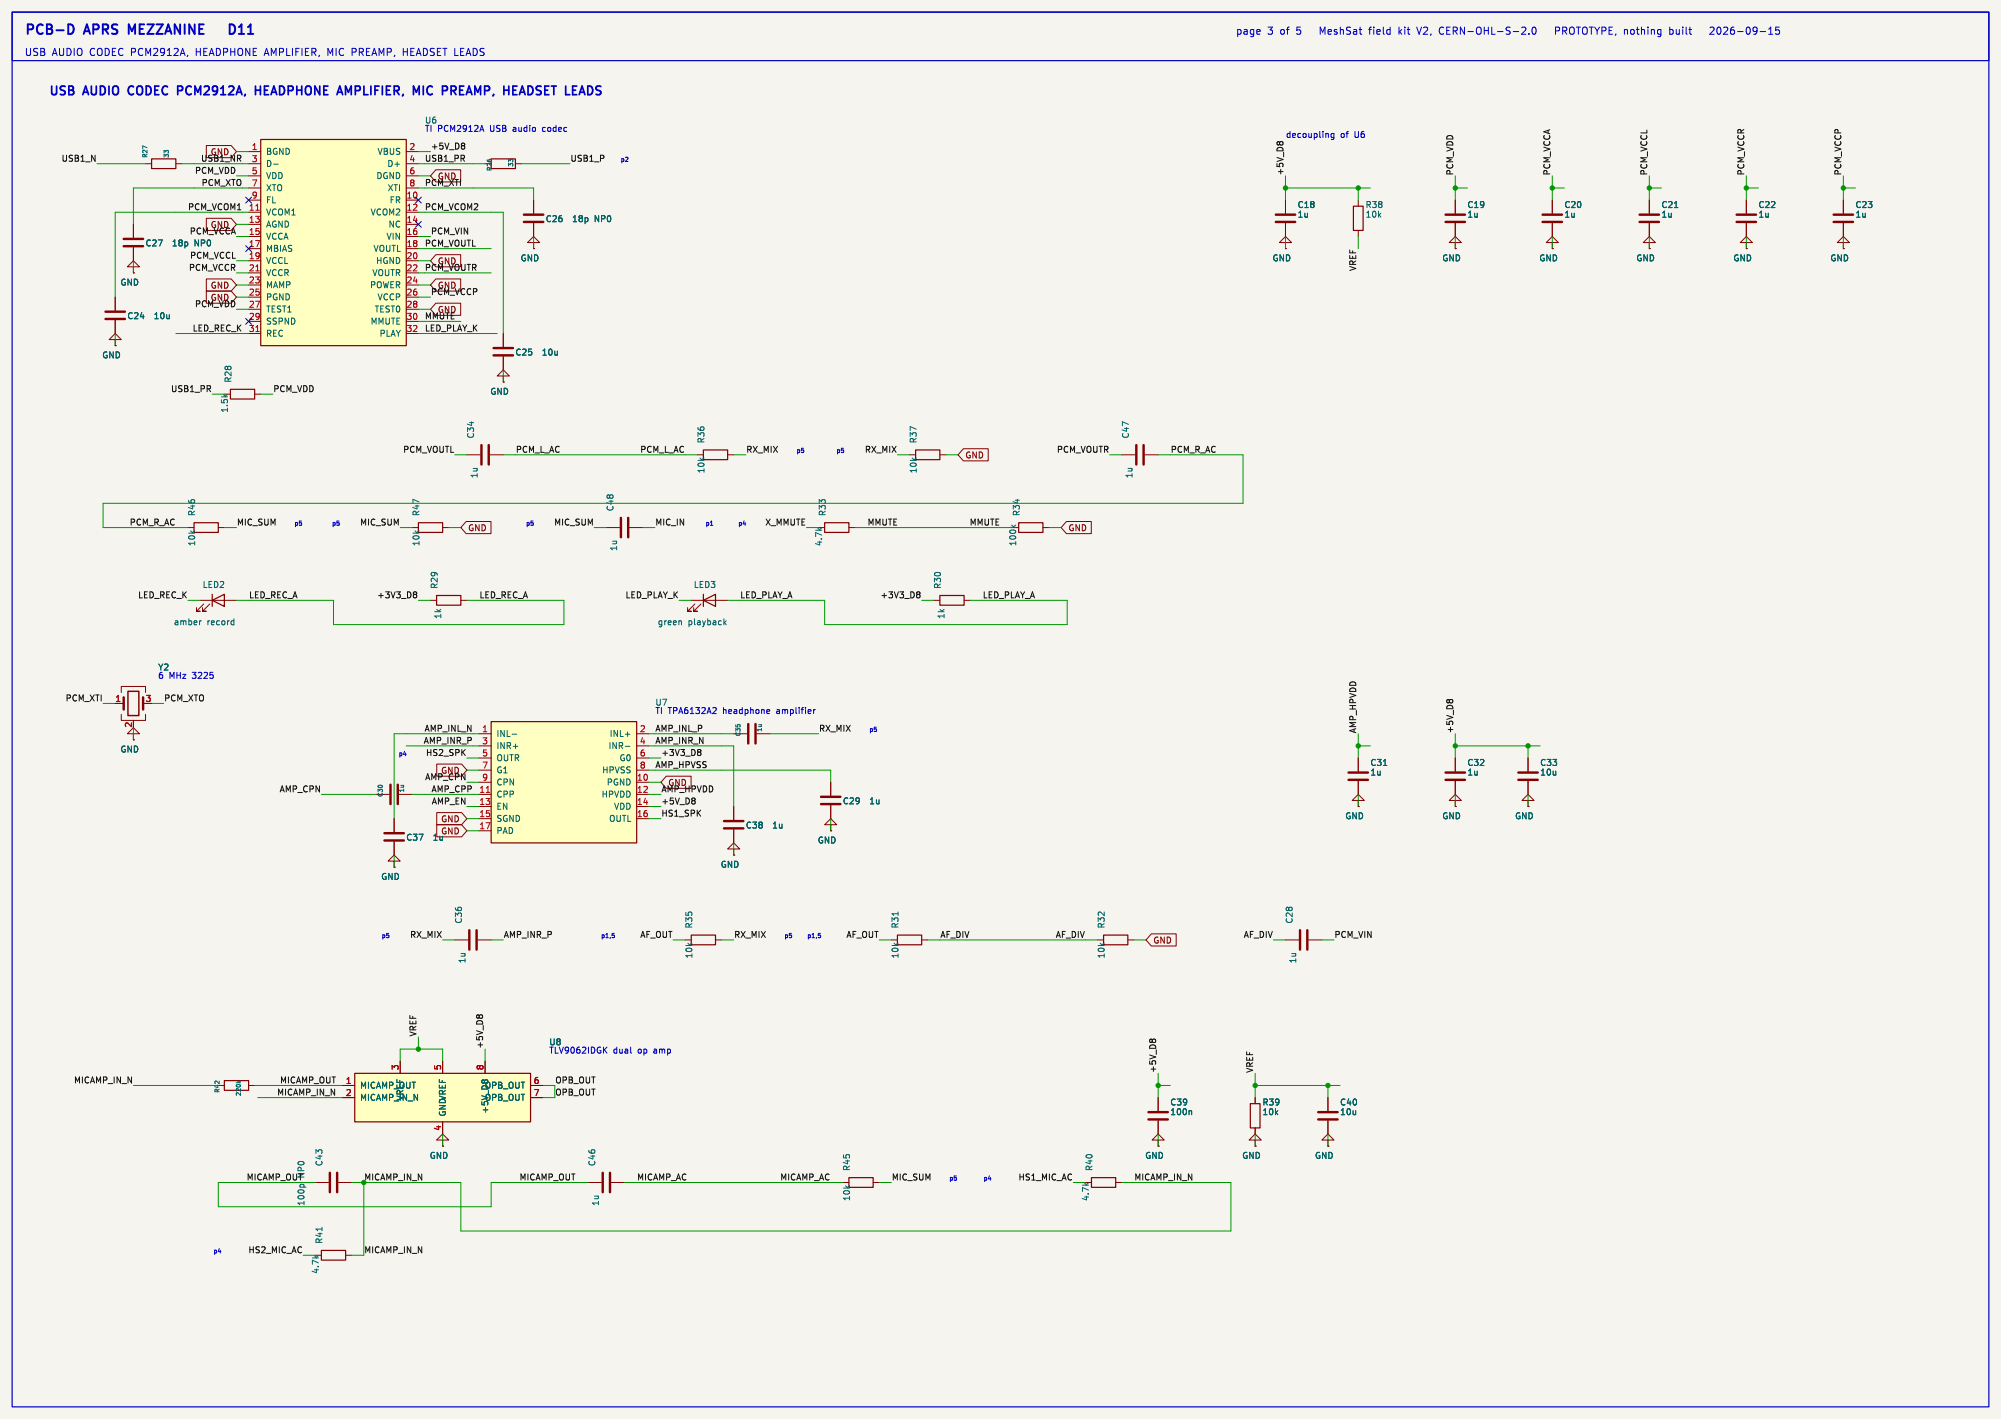
[picture p236: page 3]

USB AUDIO CODEC PCM2912A, HEADPHONE AMPLIFIER, MIC PREAMP, HEADSET LEADS

GND C⁴⁴ 1n NP⁰ R³⁷ 10k

GND GND GND GND GND

INR+ 3 OUTR 5 G1 7 CPN 9 CPP 11 EN 13 SGND 15 PAD 17

# 100n C⁵ 47u 6.3V X⁵R ¹²¹⁰

# 4 U10 R¹⁸ 15k

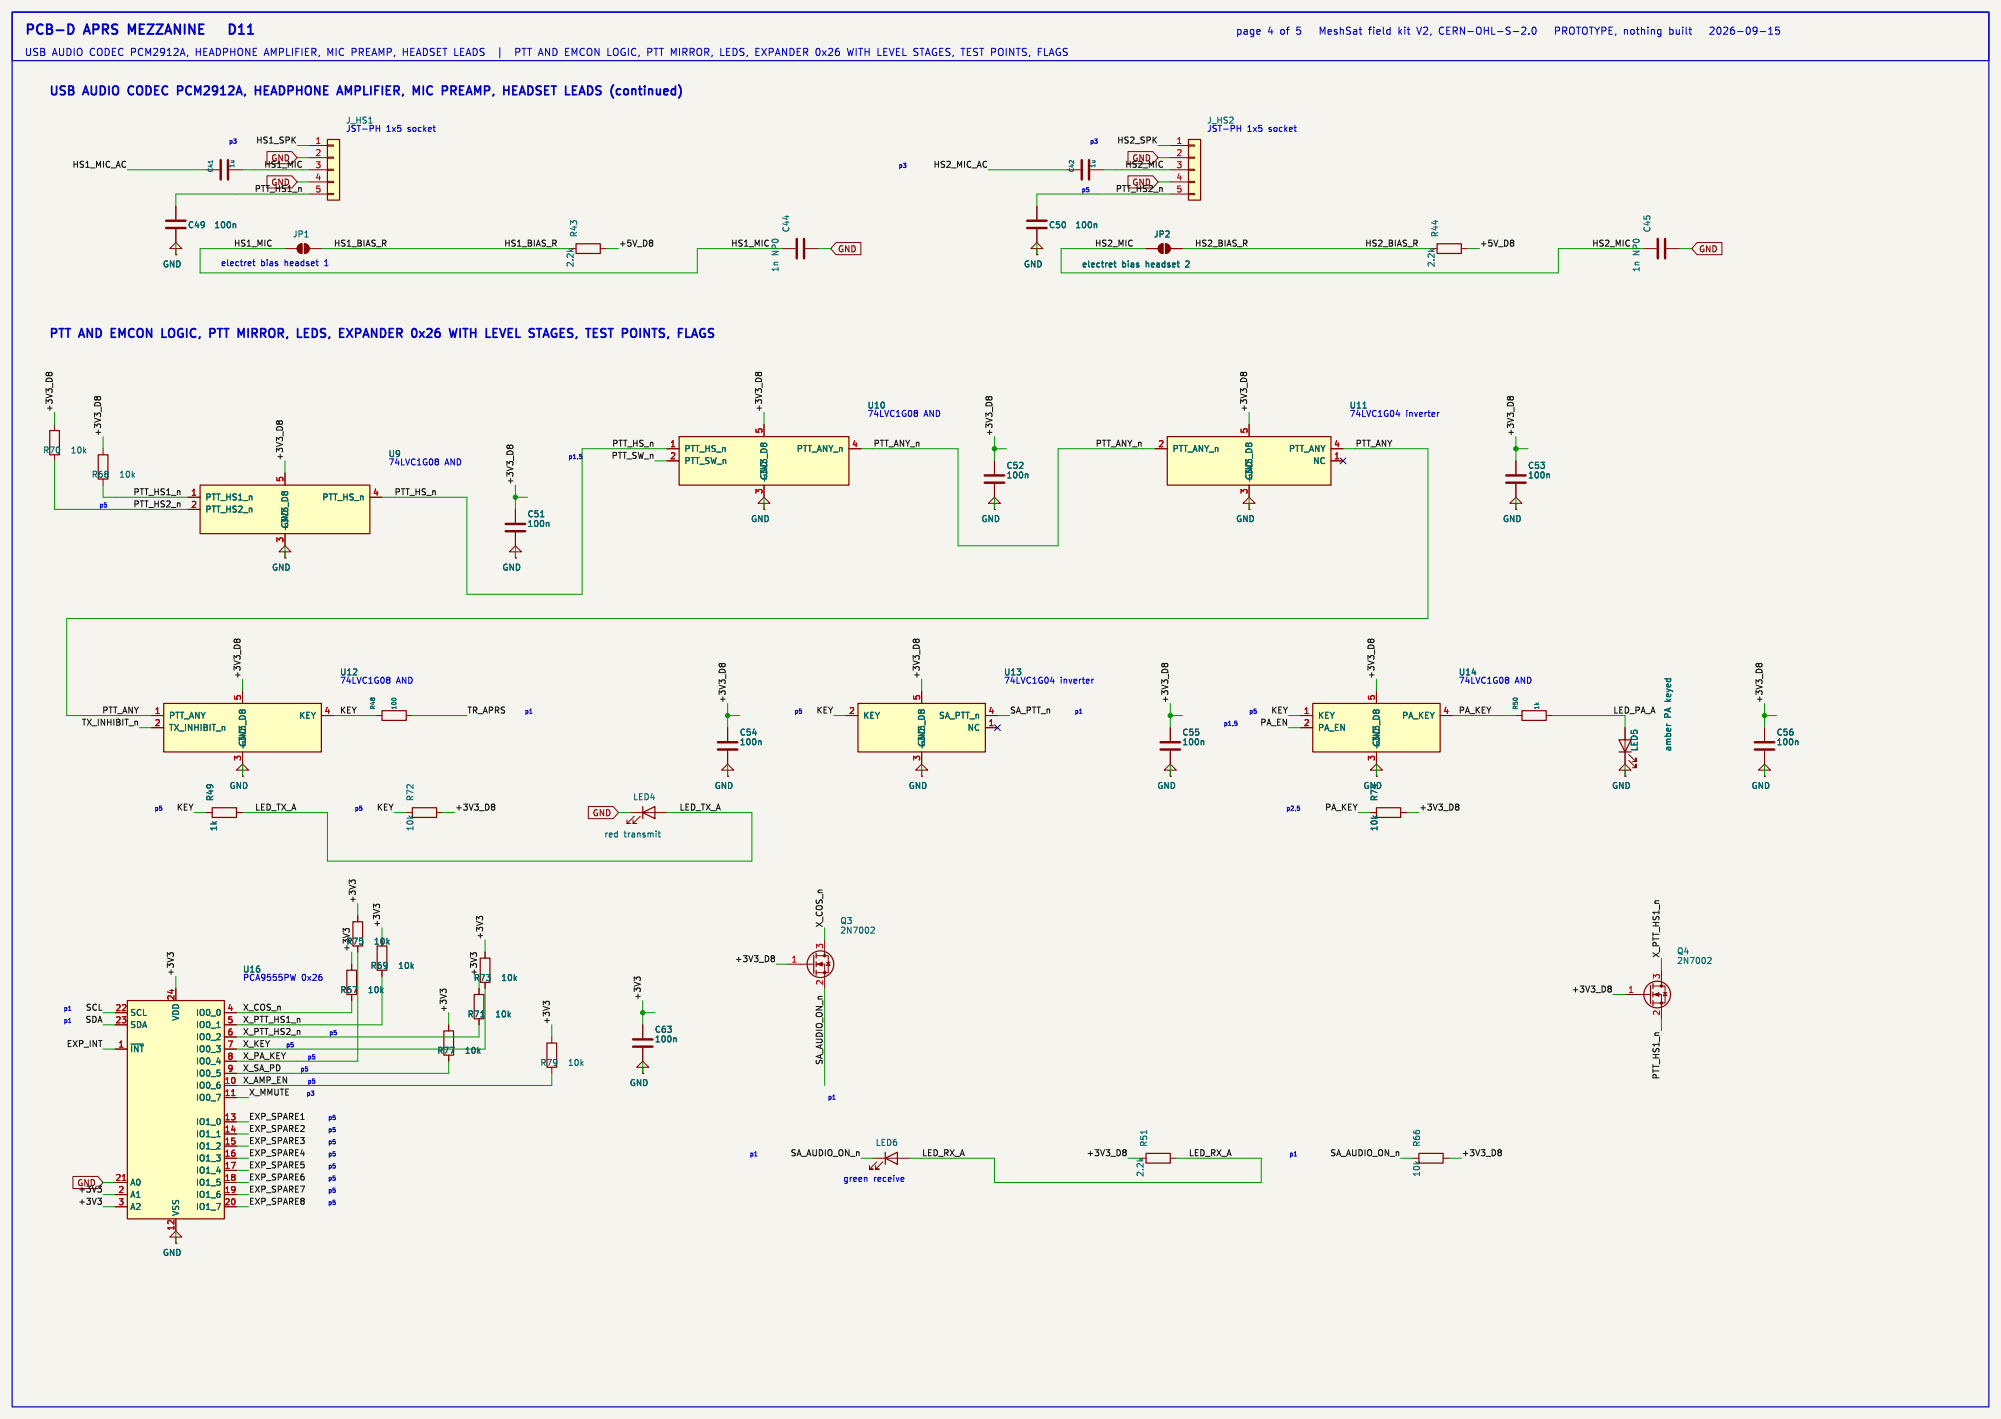
[picture p237: page 4]

GND C⁴⁴ 1n NP⁰ R³⁷ 10k

# 2N7002 D¹ SMBJ5.0A

# 2N7002 GND

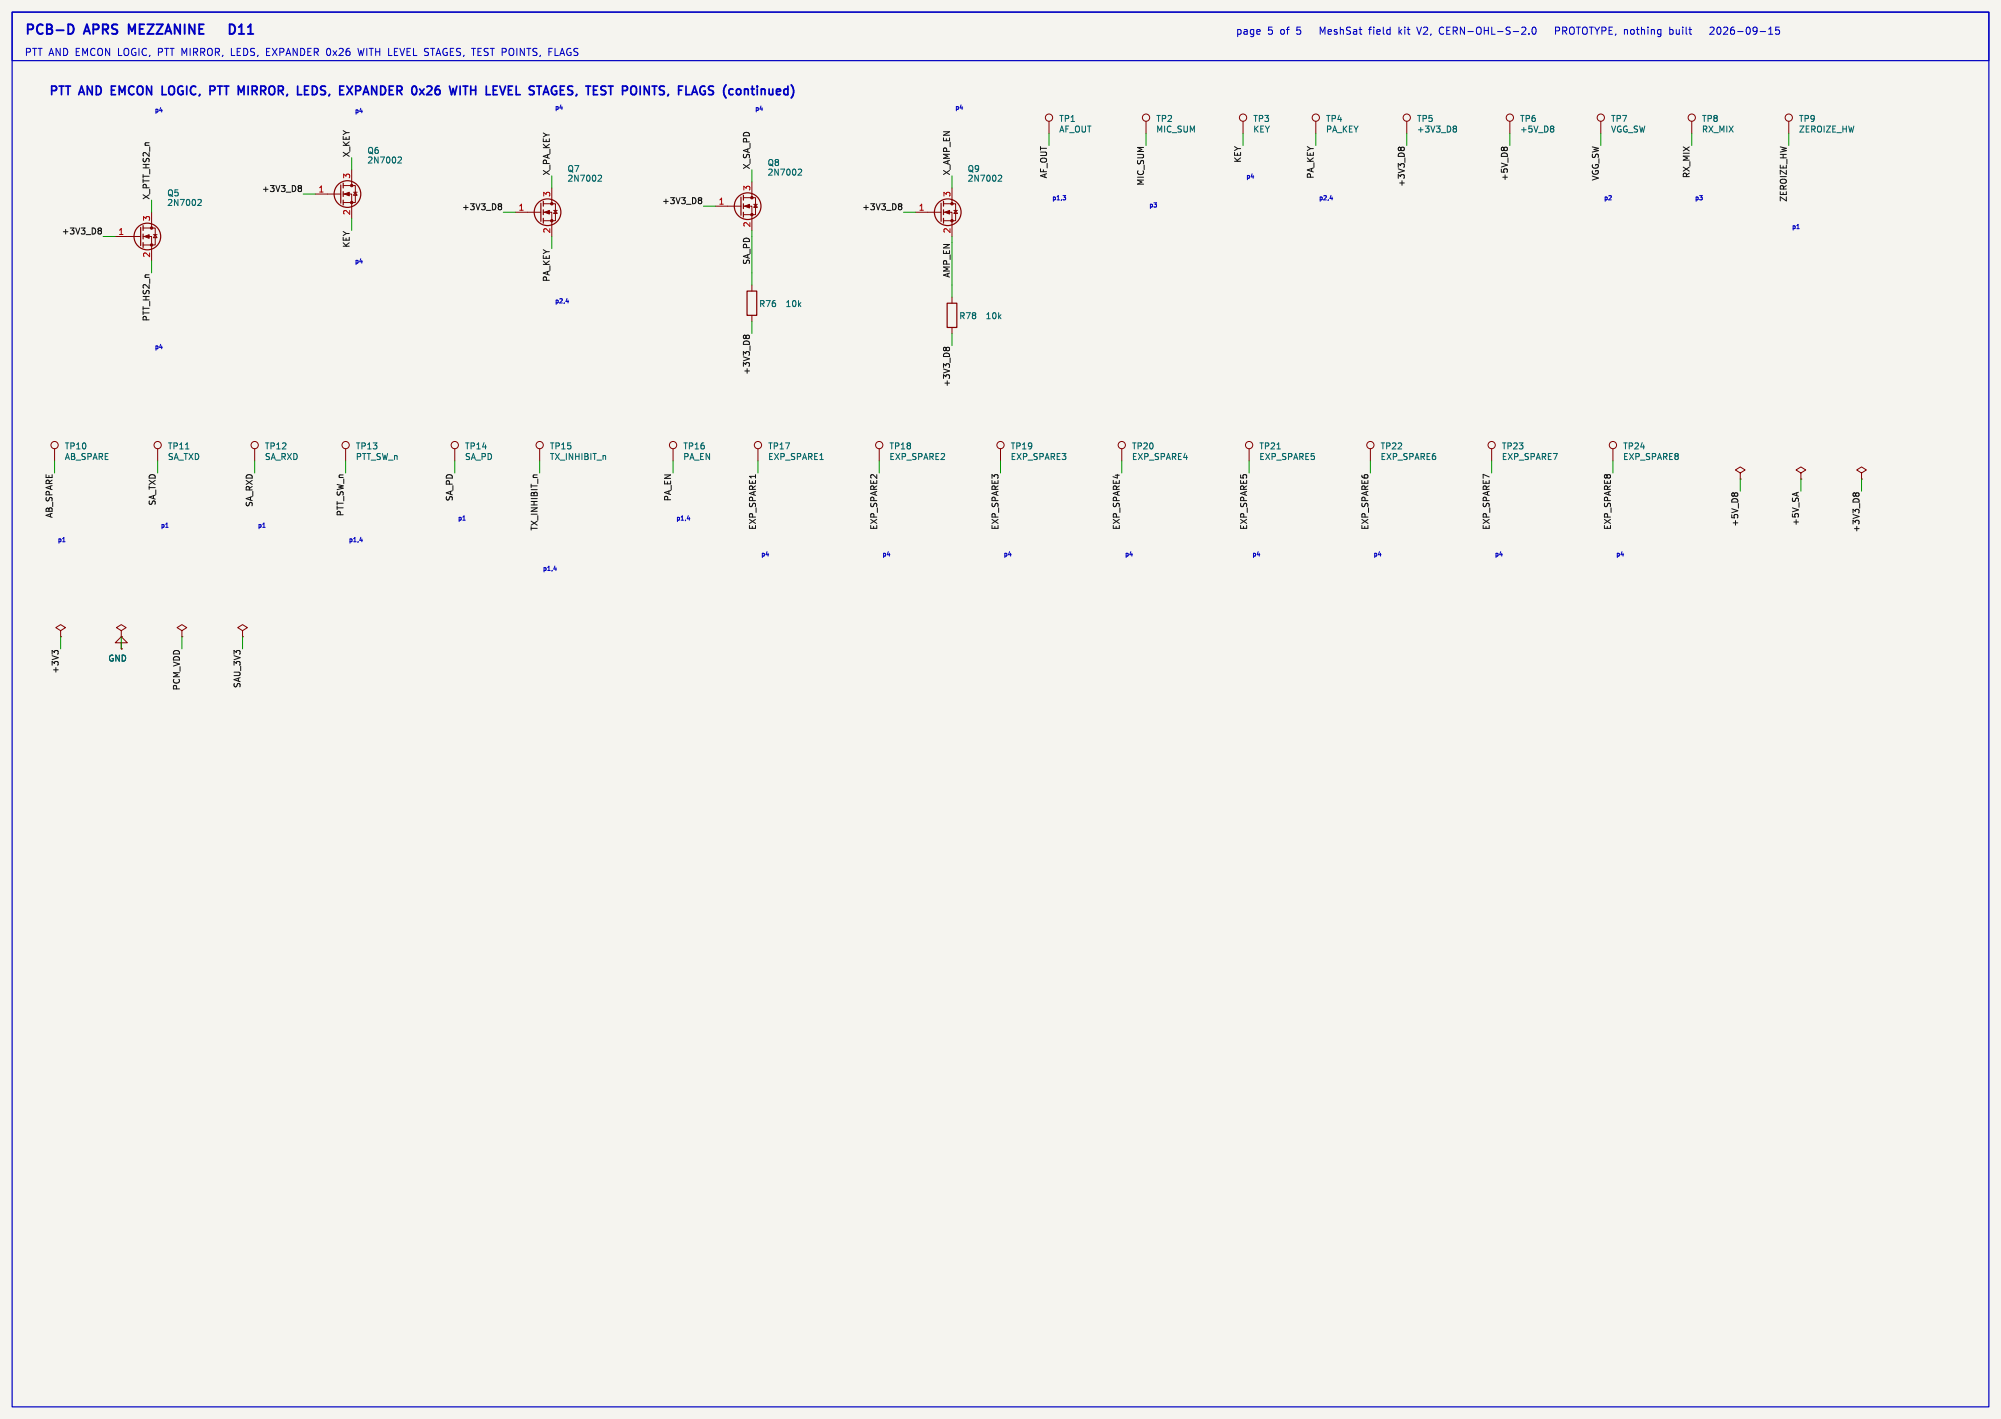
[picture p238: page 5]
