meshsat/meshsat-fieldkit/v2/release/revA/boards/meshsat-pcb-e-revA-E9/pcb-e1-dock-schematic.pdf

J_BATT HS_S 1 DC_P 2 HS_UVLO 3 HS_OVLO 4 HS_TIMER 6 | GND_V
PACK ENTRY: BB-2590/U | CABLE ON XT60, 25 A BLADE, PADS TO THE BLOCK, SMBUS HEADER

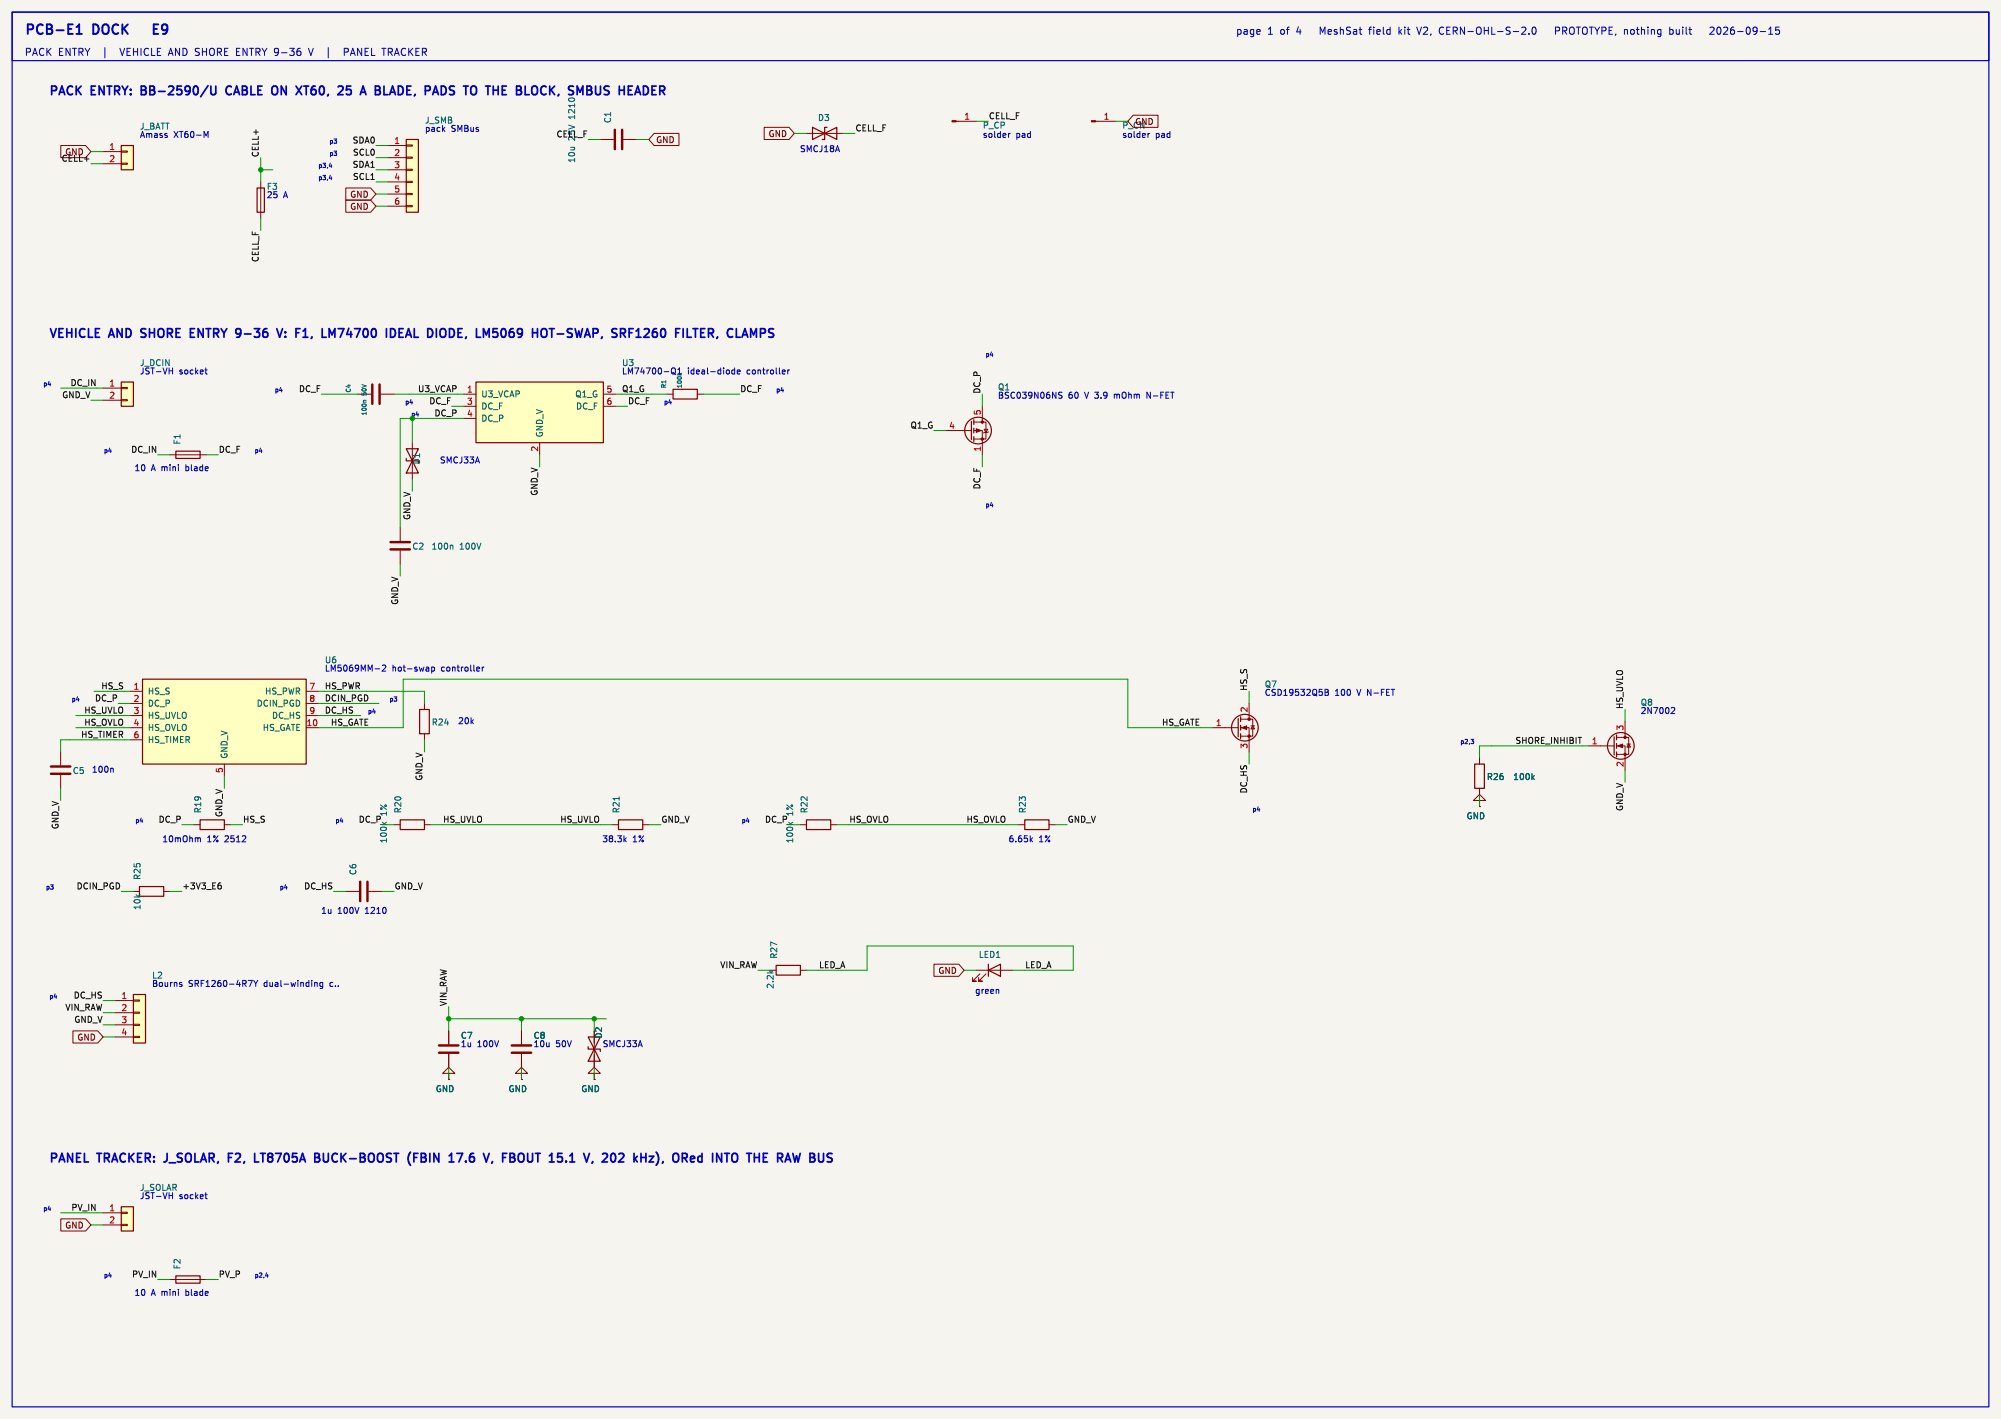
[picture p239: page 1]

PANEL TRACKER: J_SOLAR, F2, LT8705A BUCK-BOOST (FBIN 17.6 V, FBOUT 15.1 V, 202 kHz), ORed INTO THE RAW BUS

TRK_SW2 | GEIGER_IN
TRK_SW2 TRK_BOOST2 TRK_BOOST1 | TRK_SHDN | GND_V

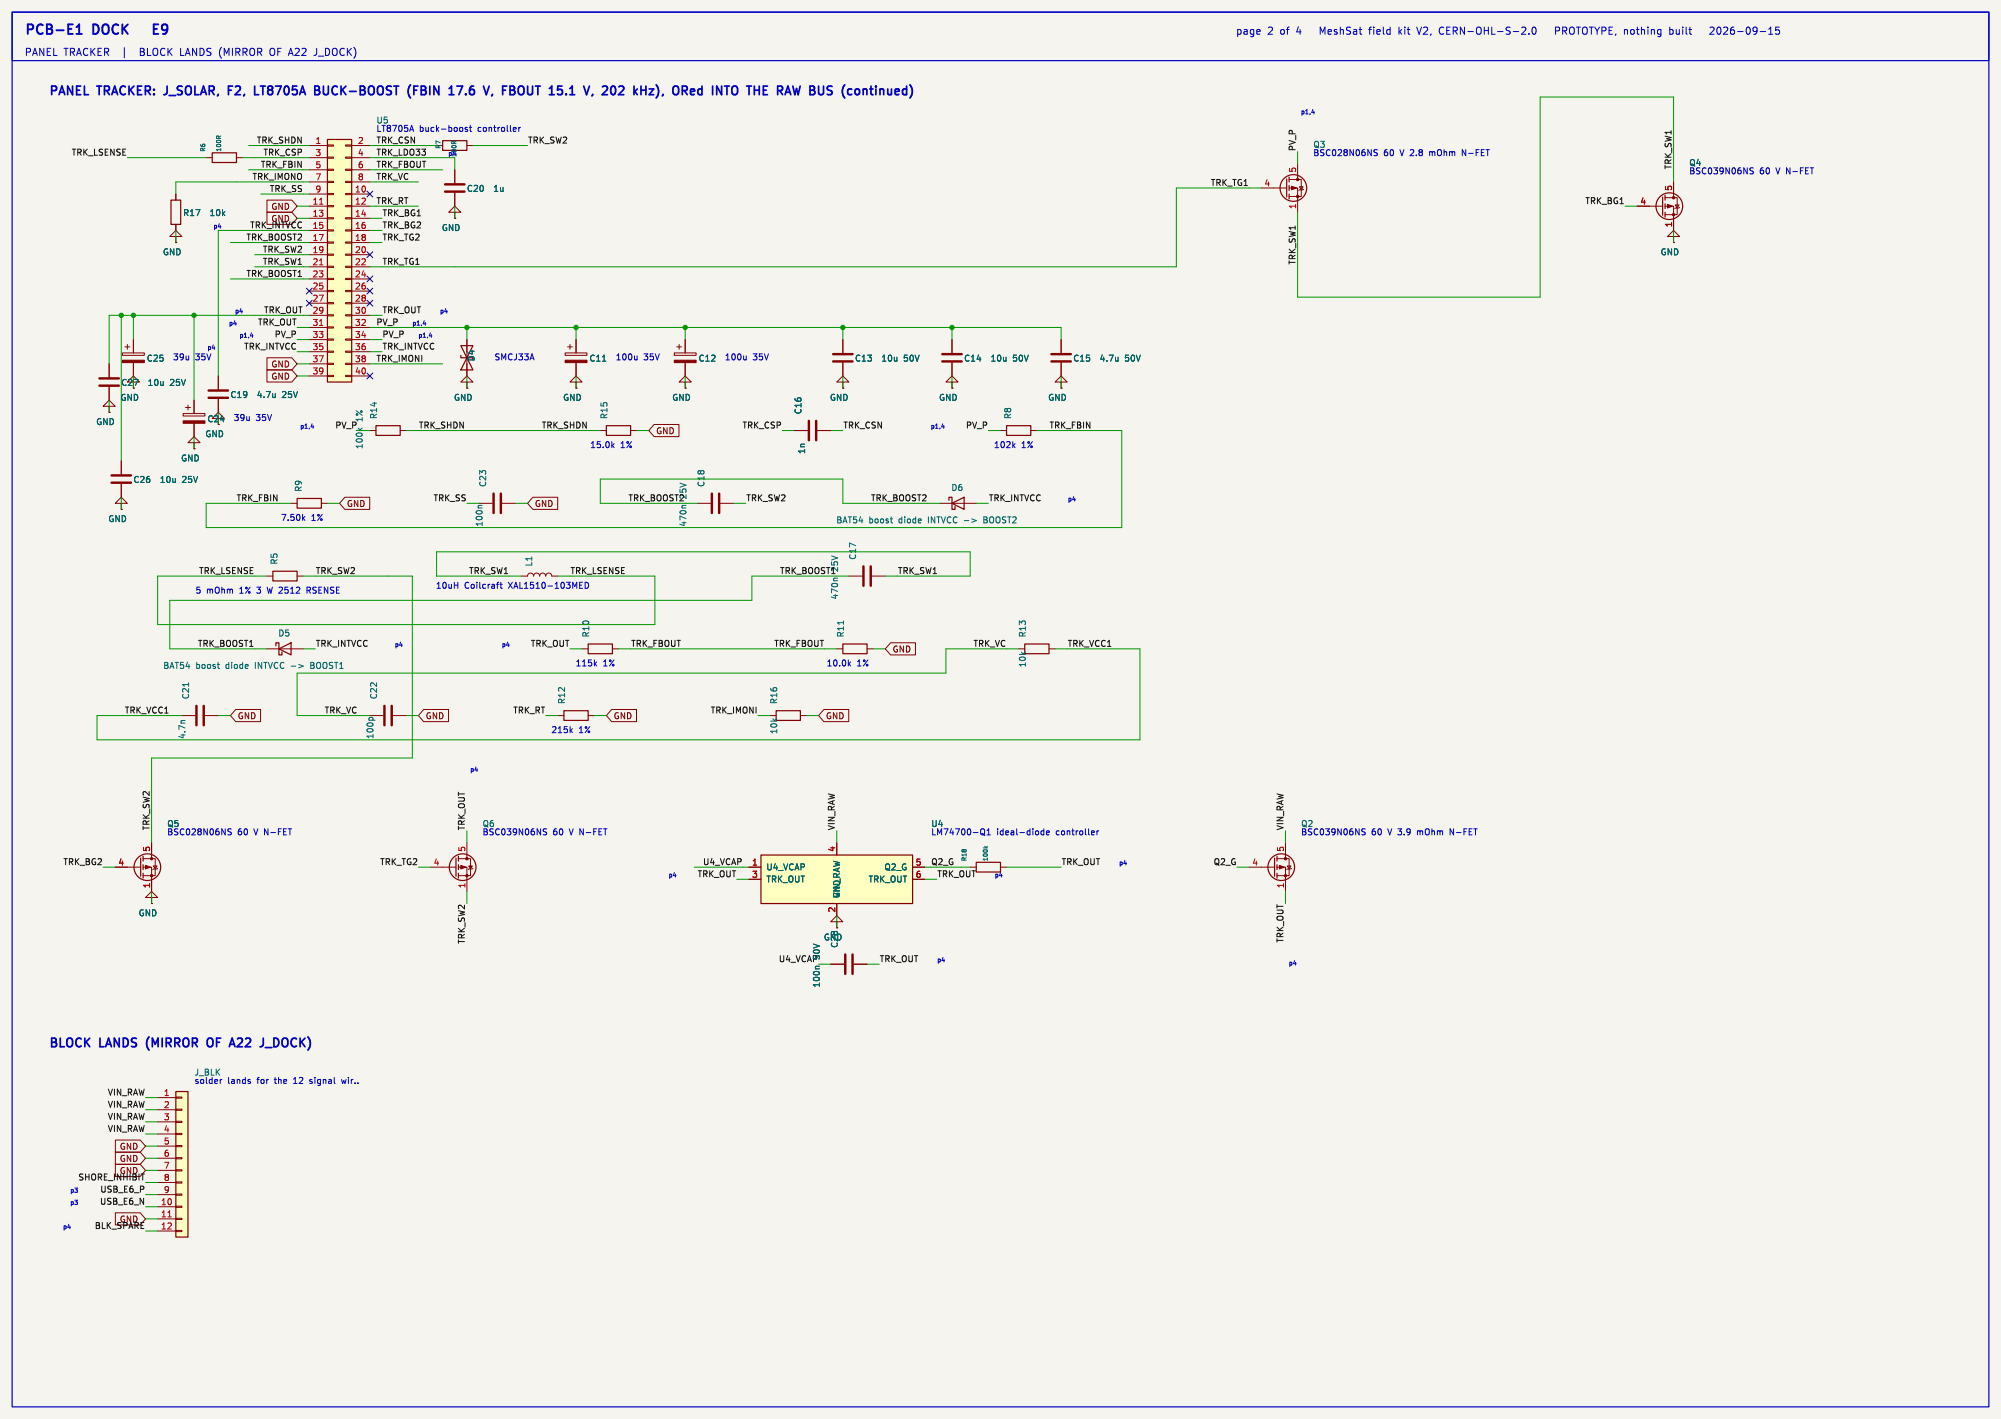
[picture p240: page 2]

PANEL TRACKER: J_SOLAR, F2, LT8705A BUCK-BOOST (FBIN 17.6 V, FBOUT 15.1 V, 202 kHz), ORed INTO THE RAW BUS (continued)

100u 35V BLOCK LANDS (MIRROR OF A22 J_DOCK)

# R35 4.7kGND

R31 | 10k JP¹ GND | GND | GND

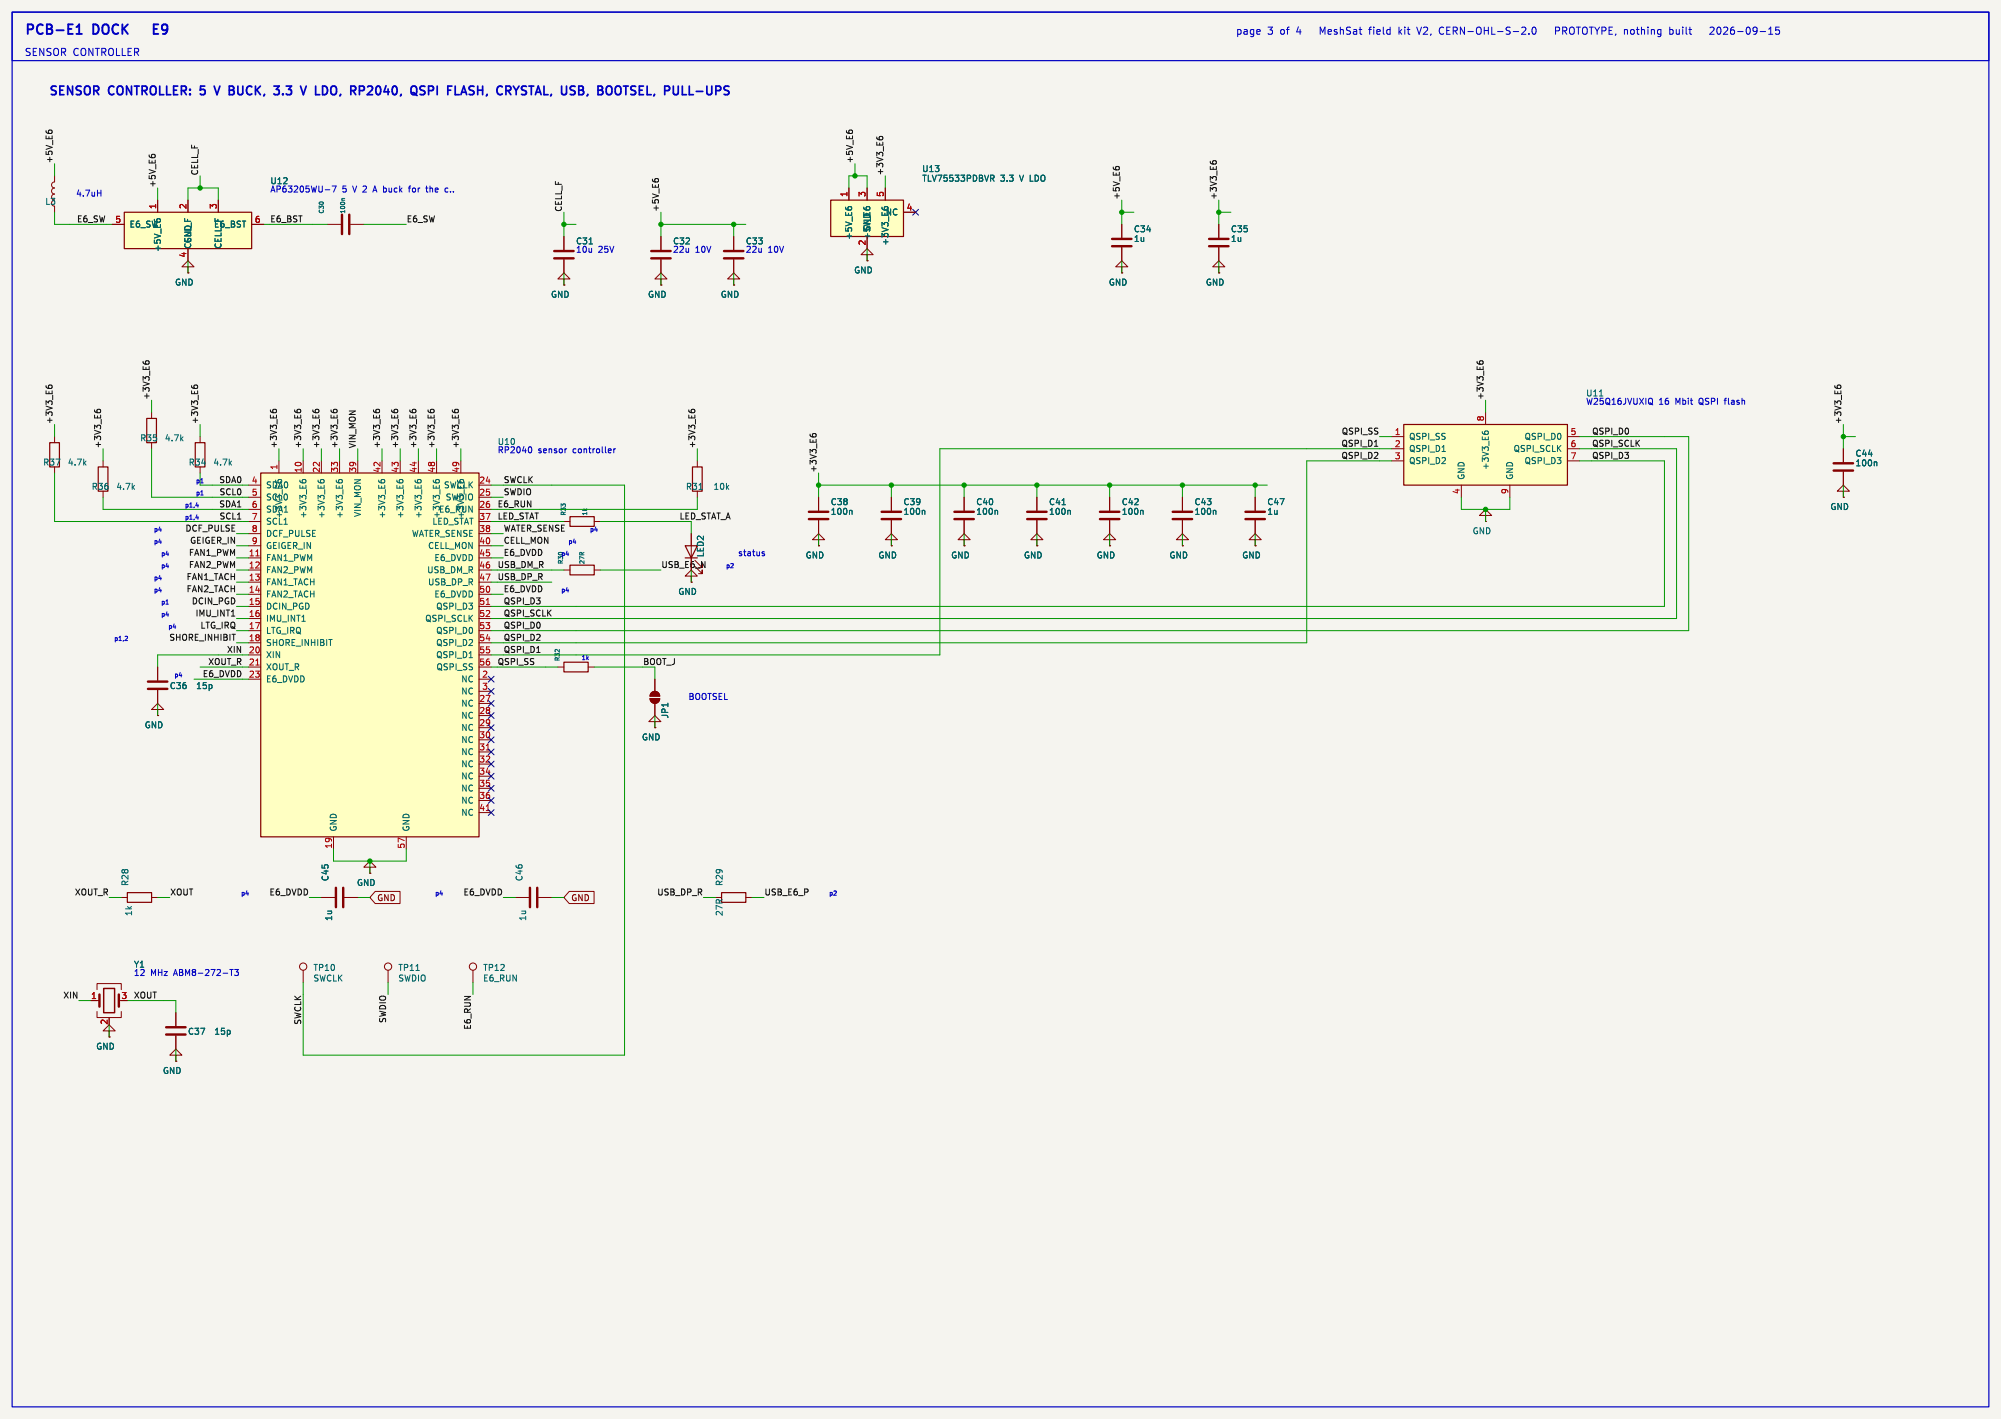
[picture p241: page 3]

1 CELL_F
LED_STAT 37 WATER_SENSE 38 CELL_MON 40 E6_DVDD 45 USB_DM_R 46 USB_DP_R 47 E6_DVDD 50 QSPI_D3 51 QSPI_SCLK 52 QSPI_D0 53 QSPI_D2 54 QSPI_D1 55 QSPI_SS 56 NC 2 NC 3 NC 27 NC 28 NC 29 NC 30 NC 31 NC 32 NC 34 NC 35 NC 36 NC 41 U10 GND

1 +3V3_E6 10 +3V3_E6 22 GND 19 +3V3_E6 33 VIN_MON 39 +3V3_E6 42 +3V3_E6 43 GND 57 +3V3_E6 44 +3V3_E6 48 +3V3_E6 49 SWCLK 24 SWDIO 25 E6_RUN 26

GND R⁴⁵ | 100R | D⁷ | SS¹⁴ flyback across fan 1 C50
100n R⁸ D⁸ | SS¹⁴ flyback across fan 2

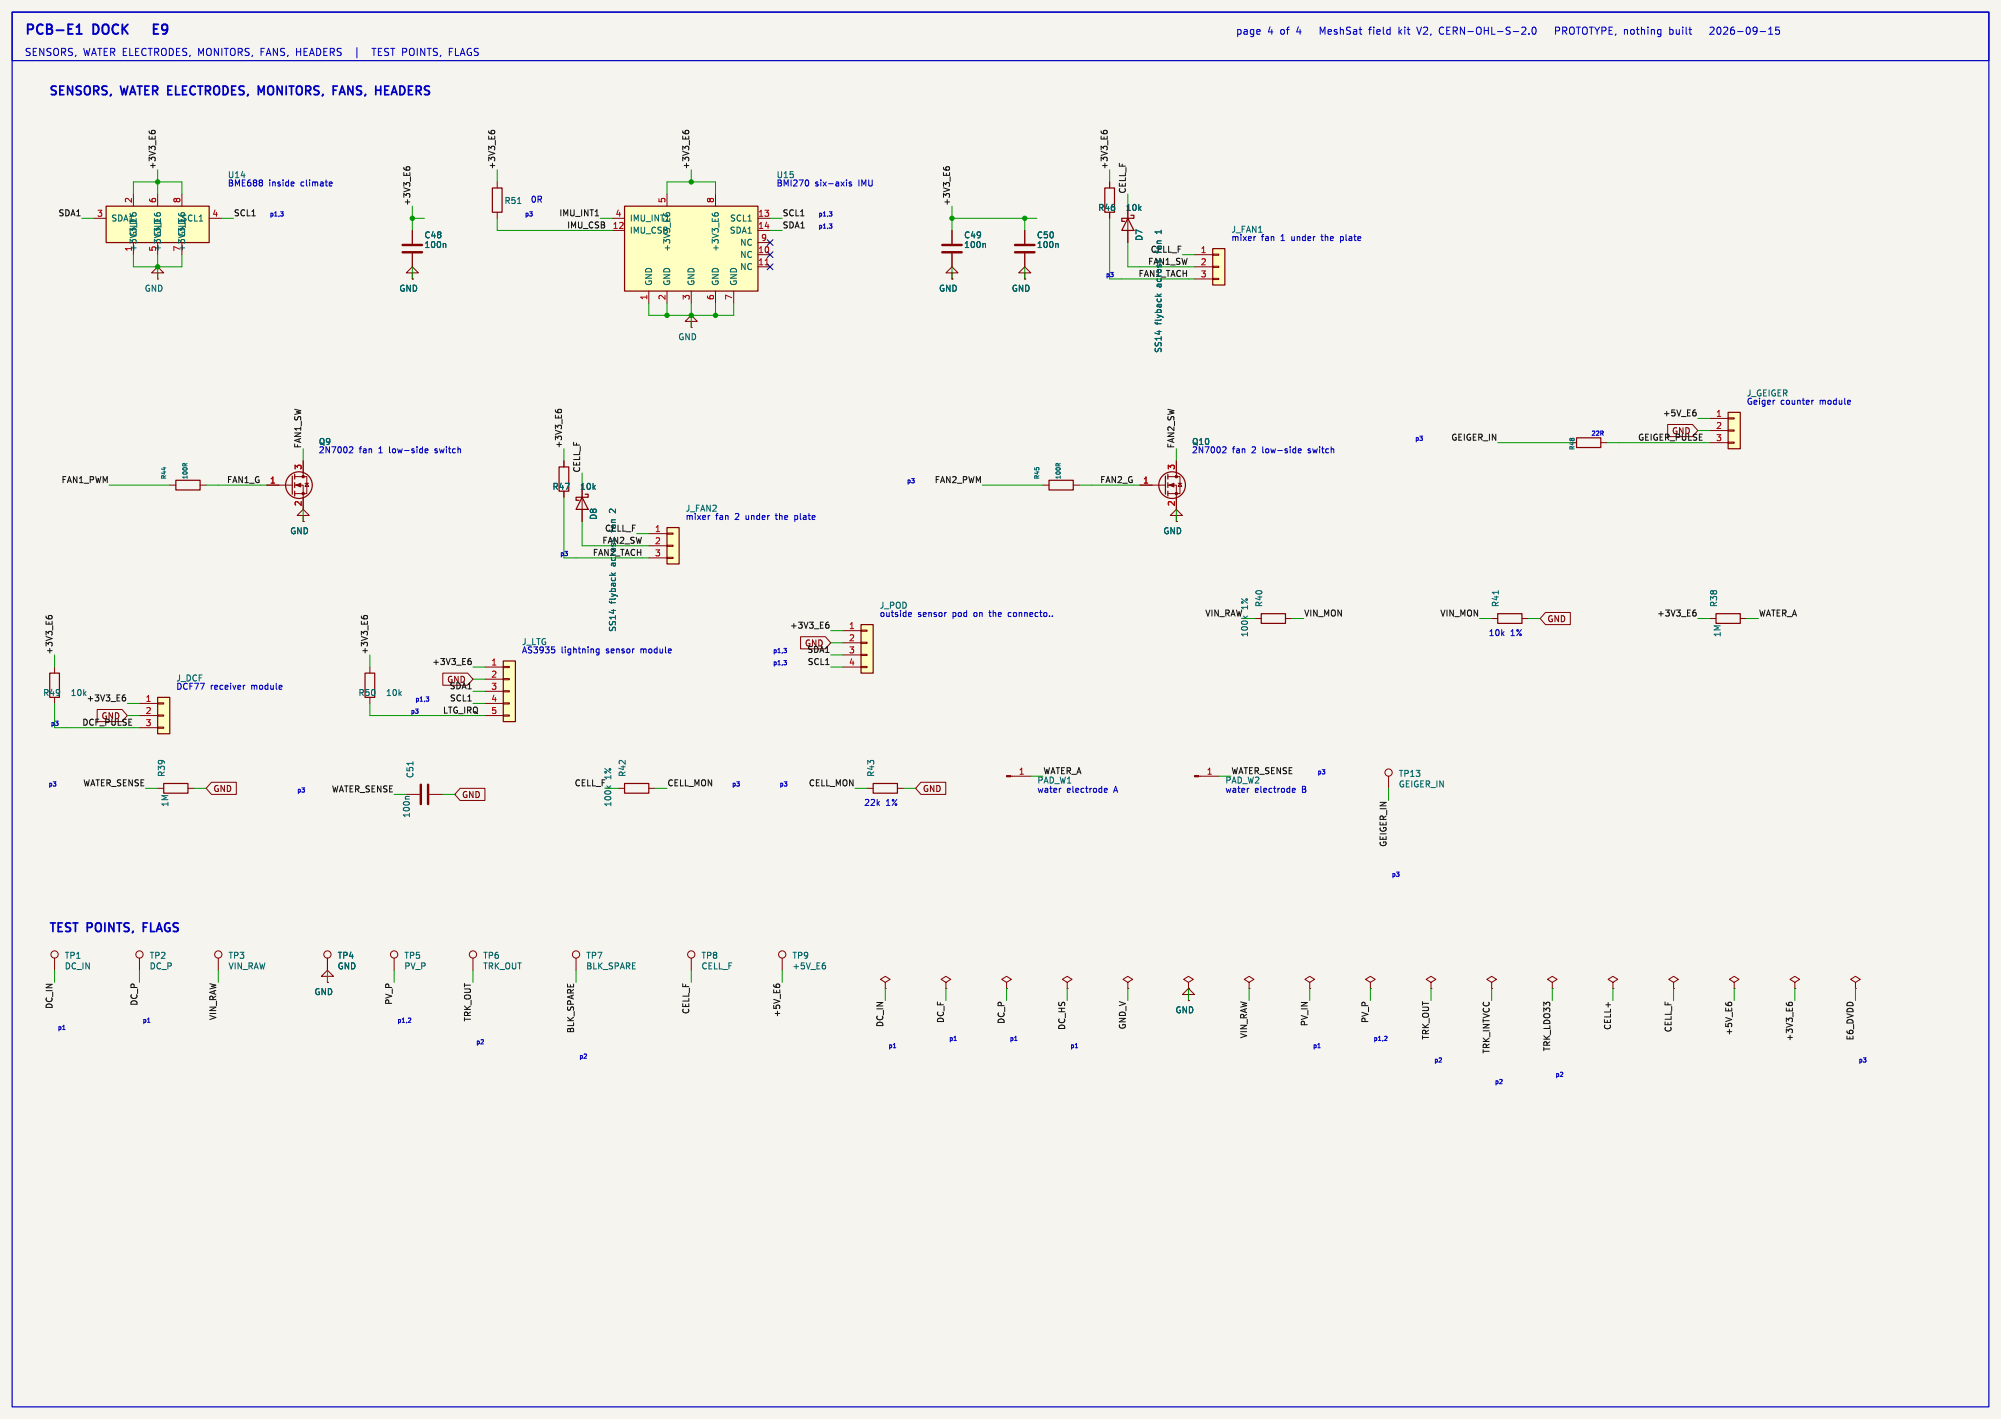
[picture p242: page 4]

J_FAN2
mixer fan 2 under the plate

J_POD
outside sensor pod on the connecto..
