meshsat/meshsat-fieldkit/v2/release/revA/boards/meshsat-pcb-p-revA-P4/pcb-p-pack-schematic.pdf

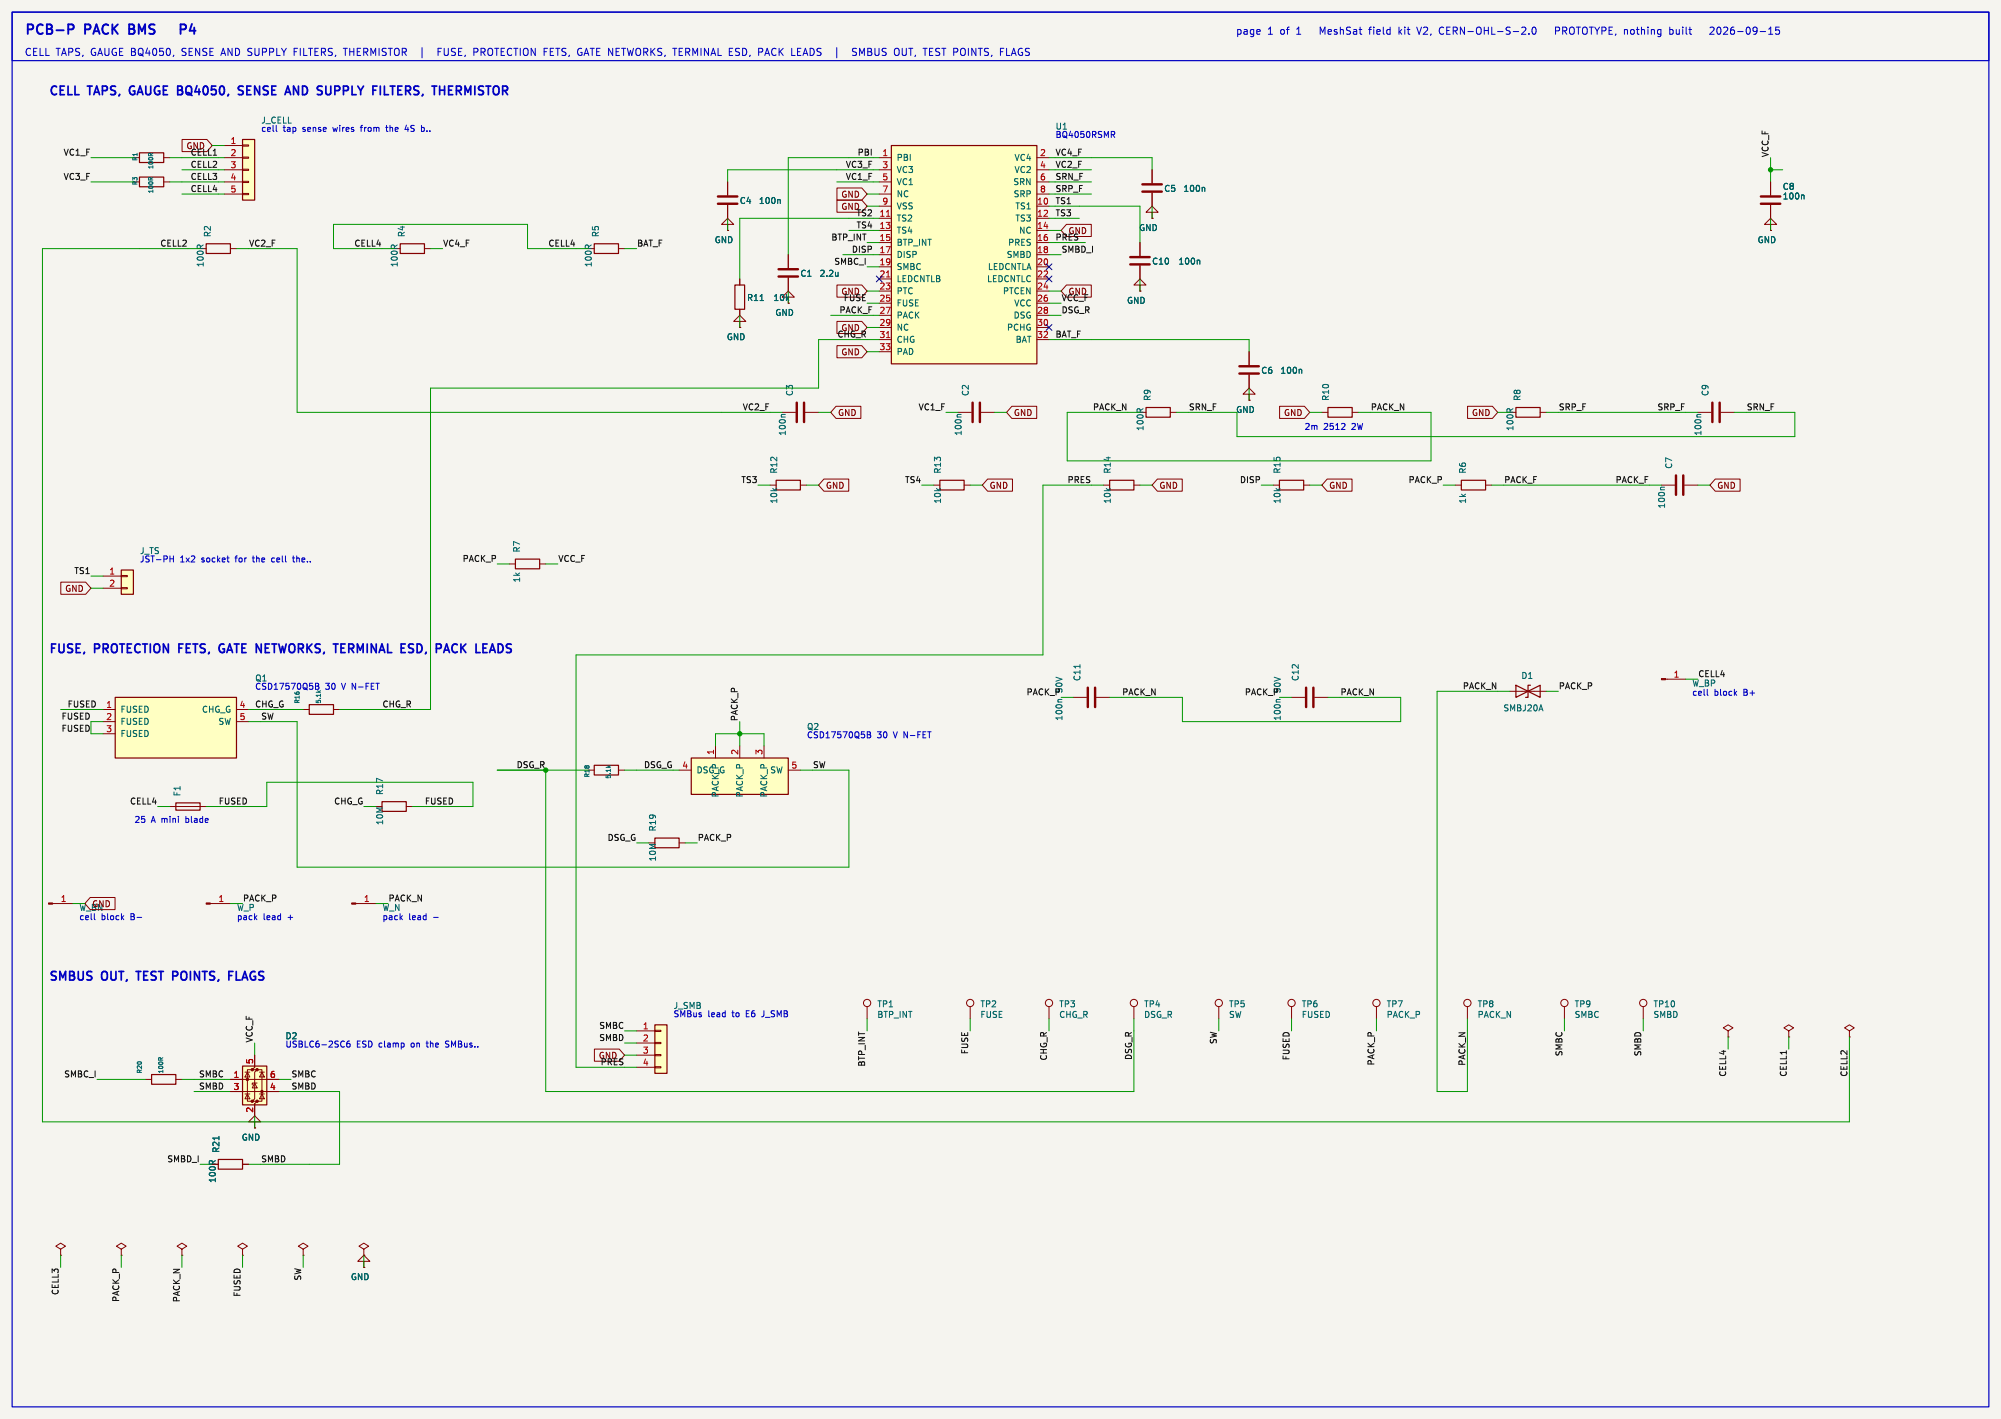
[picture p243: page 1]

CELL TAPS, GAUGE BQ4050, SENSE AND SUPPLY FILTERS, THERMISTOR

cell tap sense wires from the 4S b.. FUSE, PROTECTION FETS, GATE NETWORKS, TERMINAL ESD, PACK LEADS
