meshsat/meshsat-fieldkit/v2/release/revA/boards/meshsat-pcb-a-revA-A24/pcb-a-power-schematic.pdf

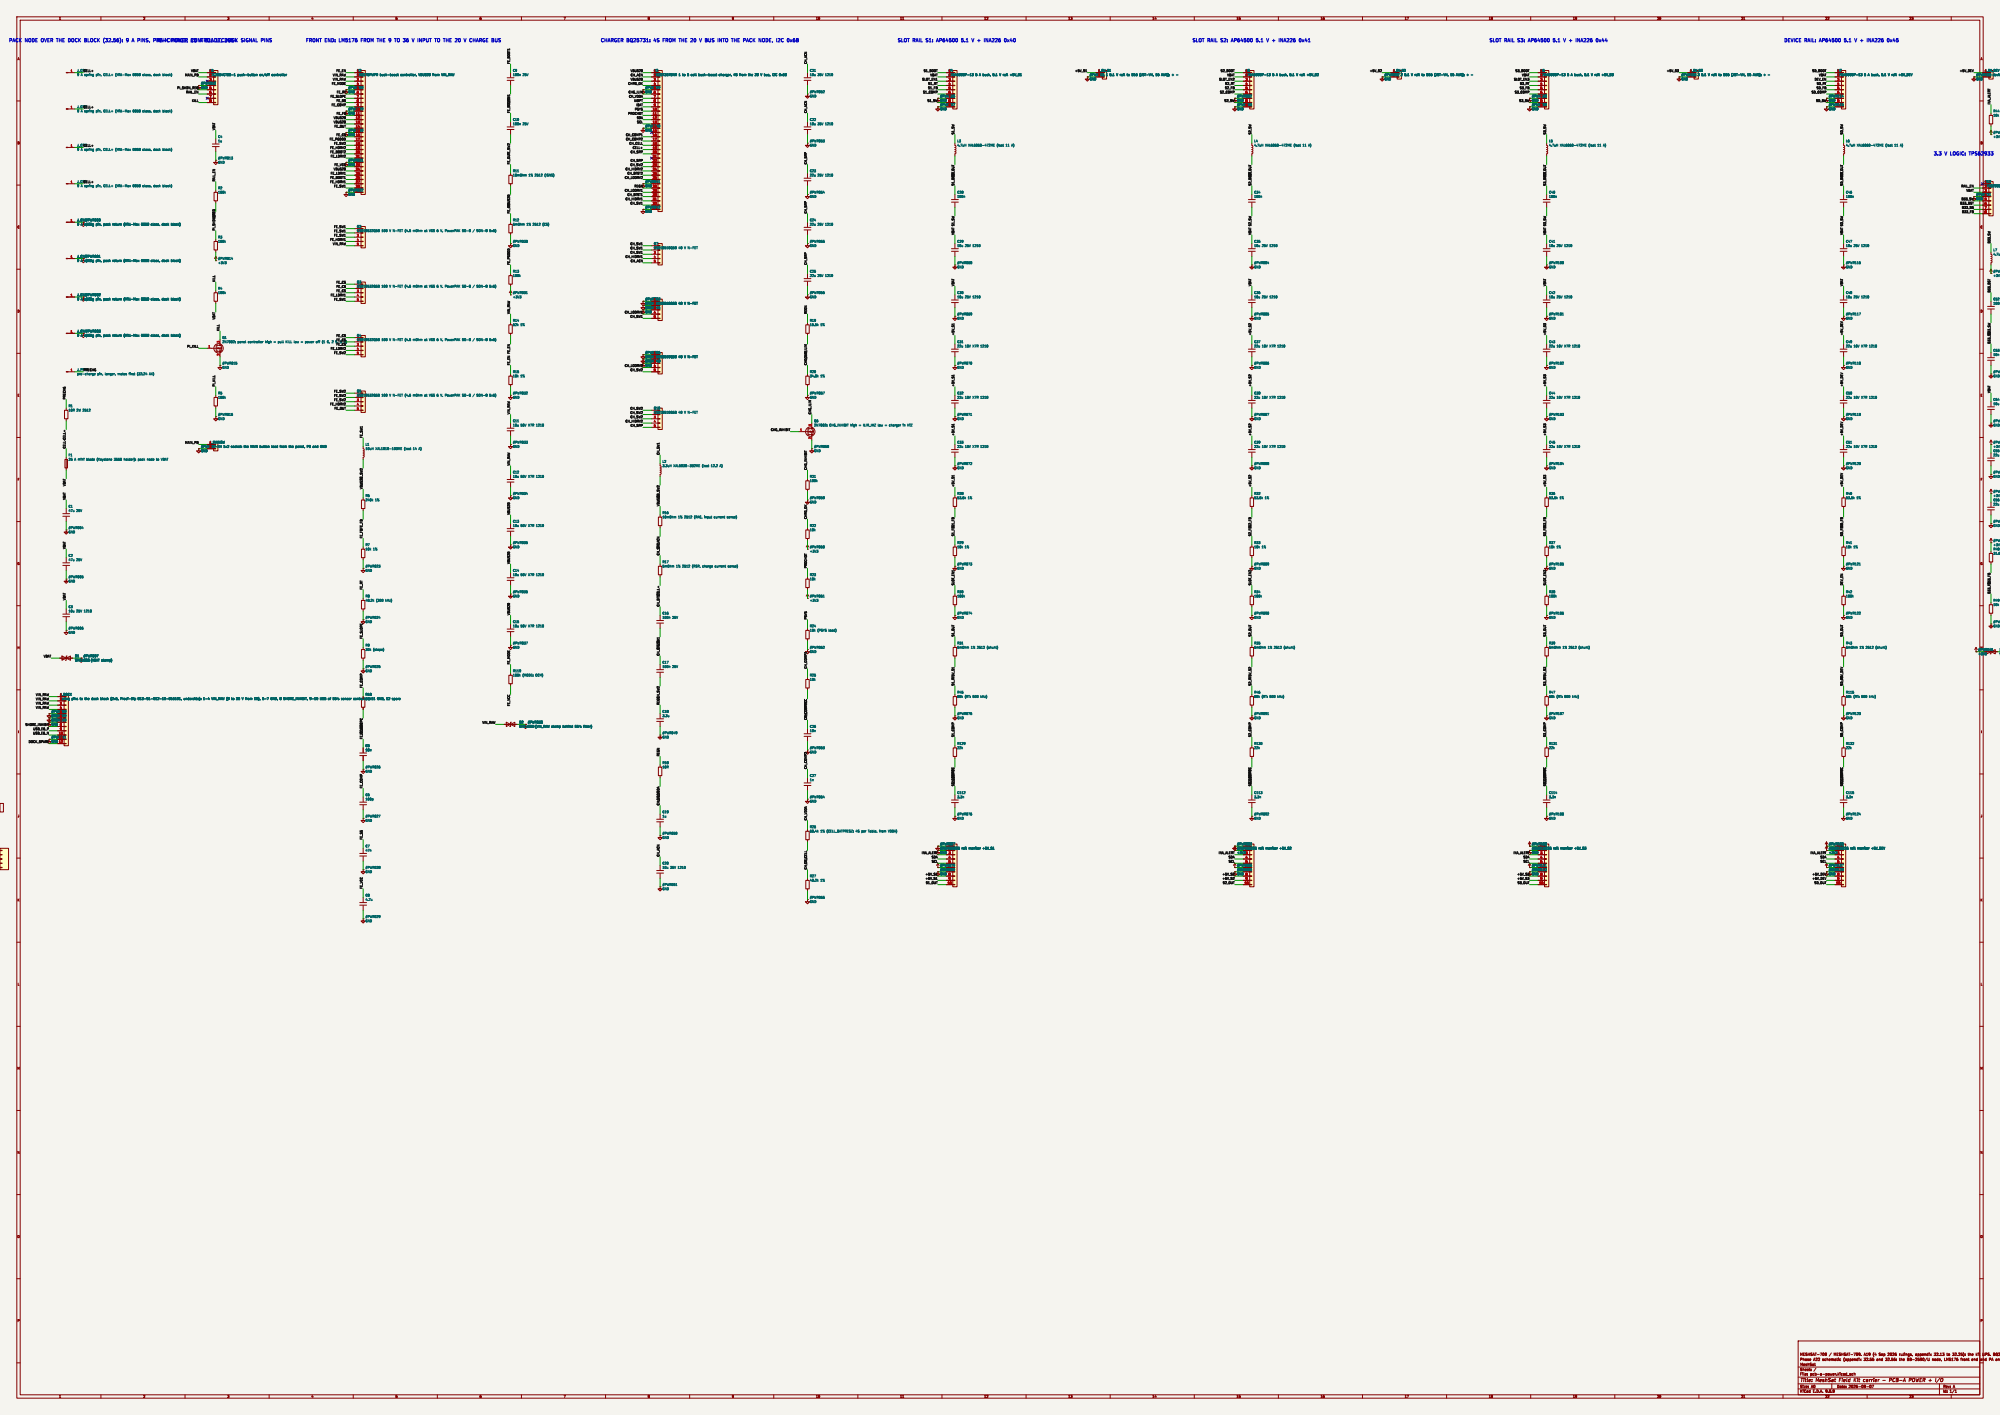
[picture p244: page 1]

J_MAINSW
JST-XH 1x2 socket: the MAIN button lead from the panel, PB and GND

5mOhm 1% 2512 (RSR, charge current sense) L2

D2SMCJ33A (VIN_RAW clamp behind E6's filter) #PWR038 GND

60.4k 1% (CELL_BATPRESZ: 4S per Table, from VDDA)

Id: 1/1 Title: MeshSat Field Kit carrier - PCB-A POWER + I/O
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
