meshsat/meshsat-fieldkit/v2/release/revA/review/PCB-A-POWER-A22/pcb-a-power-assembly-bottom-mirrored.pdf

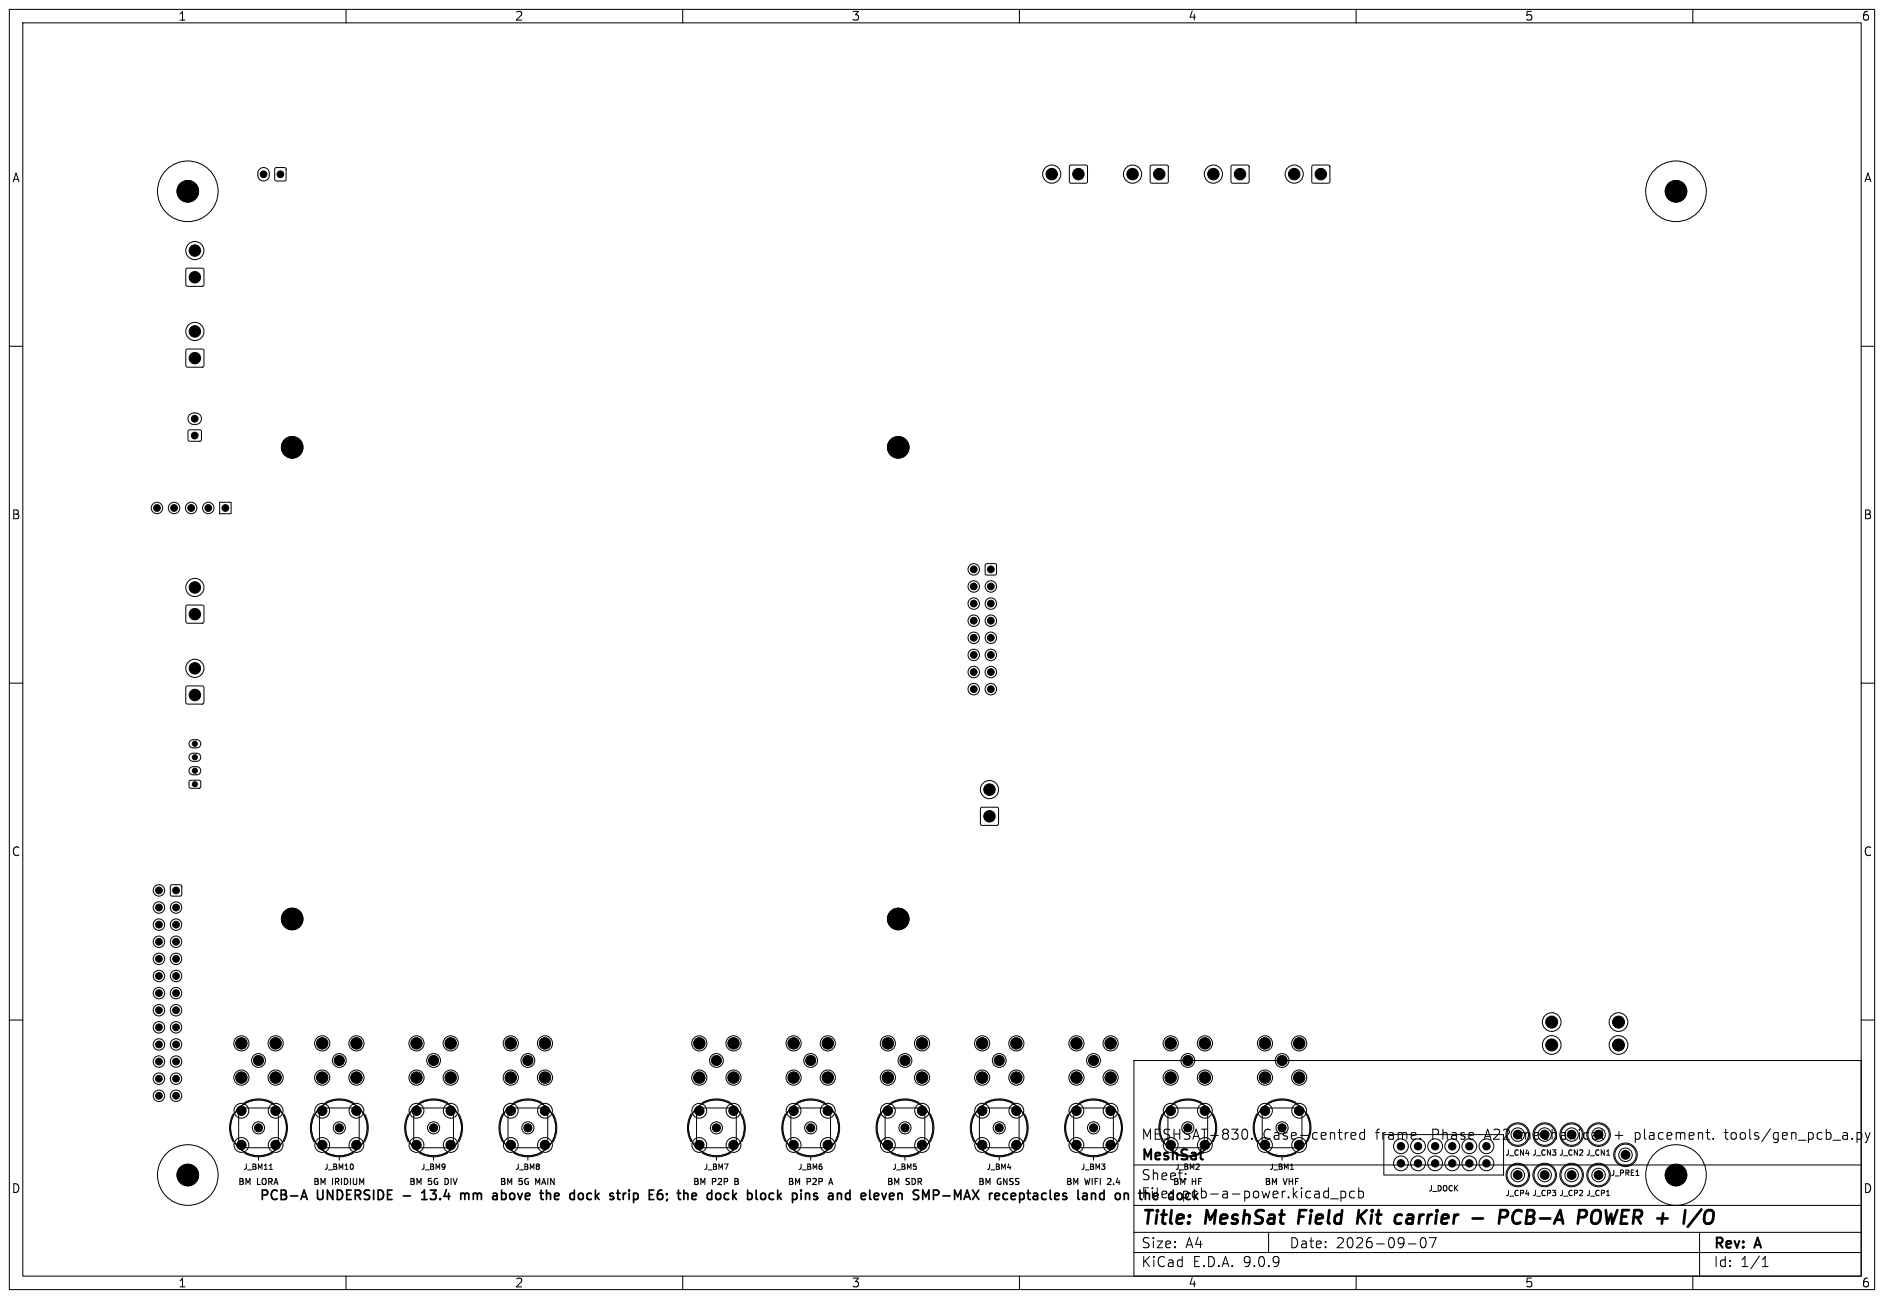
[picture p245: page 1]

Id: 1/1 Title: MeshSat Field Kit carrier - PCB-A POWER + I/O
