meshsat/meshsat-fieldkit/v2/release/revA/review/PCB-B-COMPUTE-B16/pcb-b-compute-assembly-bottom-mirrored.pdf

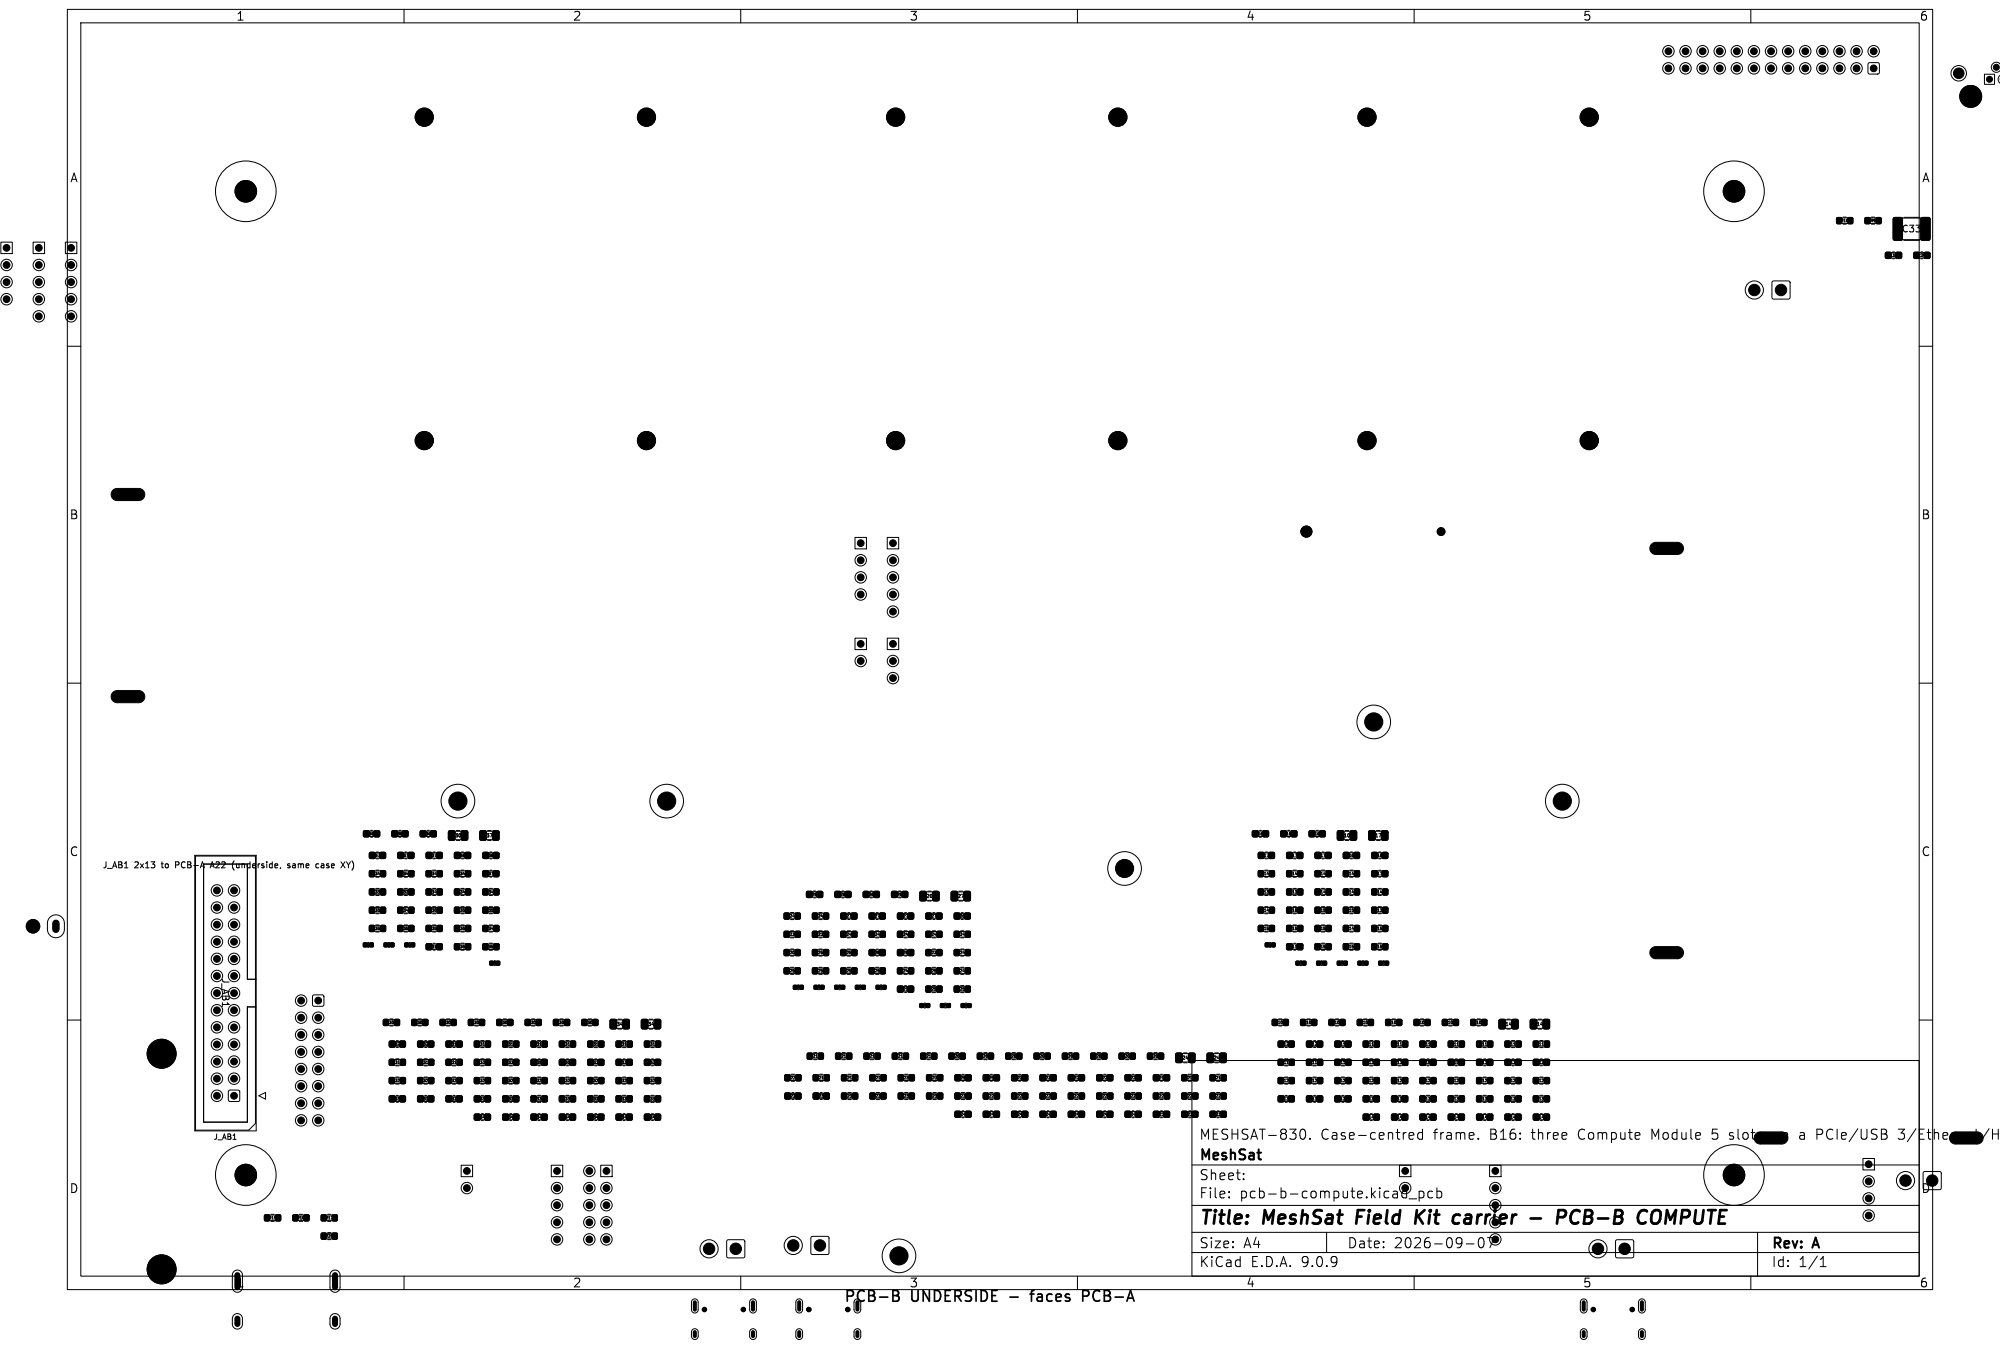
[picture p247: page 1]

Id: 1/1 Title: MeshSat Field Kit carrier - PCB-B COMPUTE
