meshsat/meshsat-fieldkit/v2/release/revA/review/PCB-B-COMPUTE-B16/pcb-b-compute-assembly-top.pdf

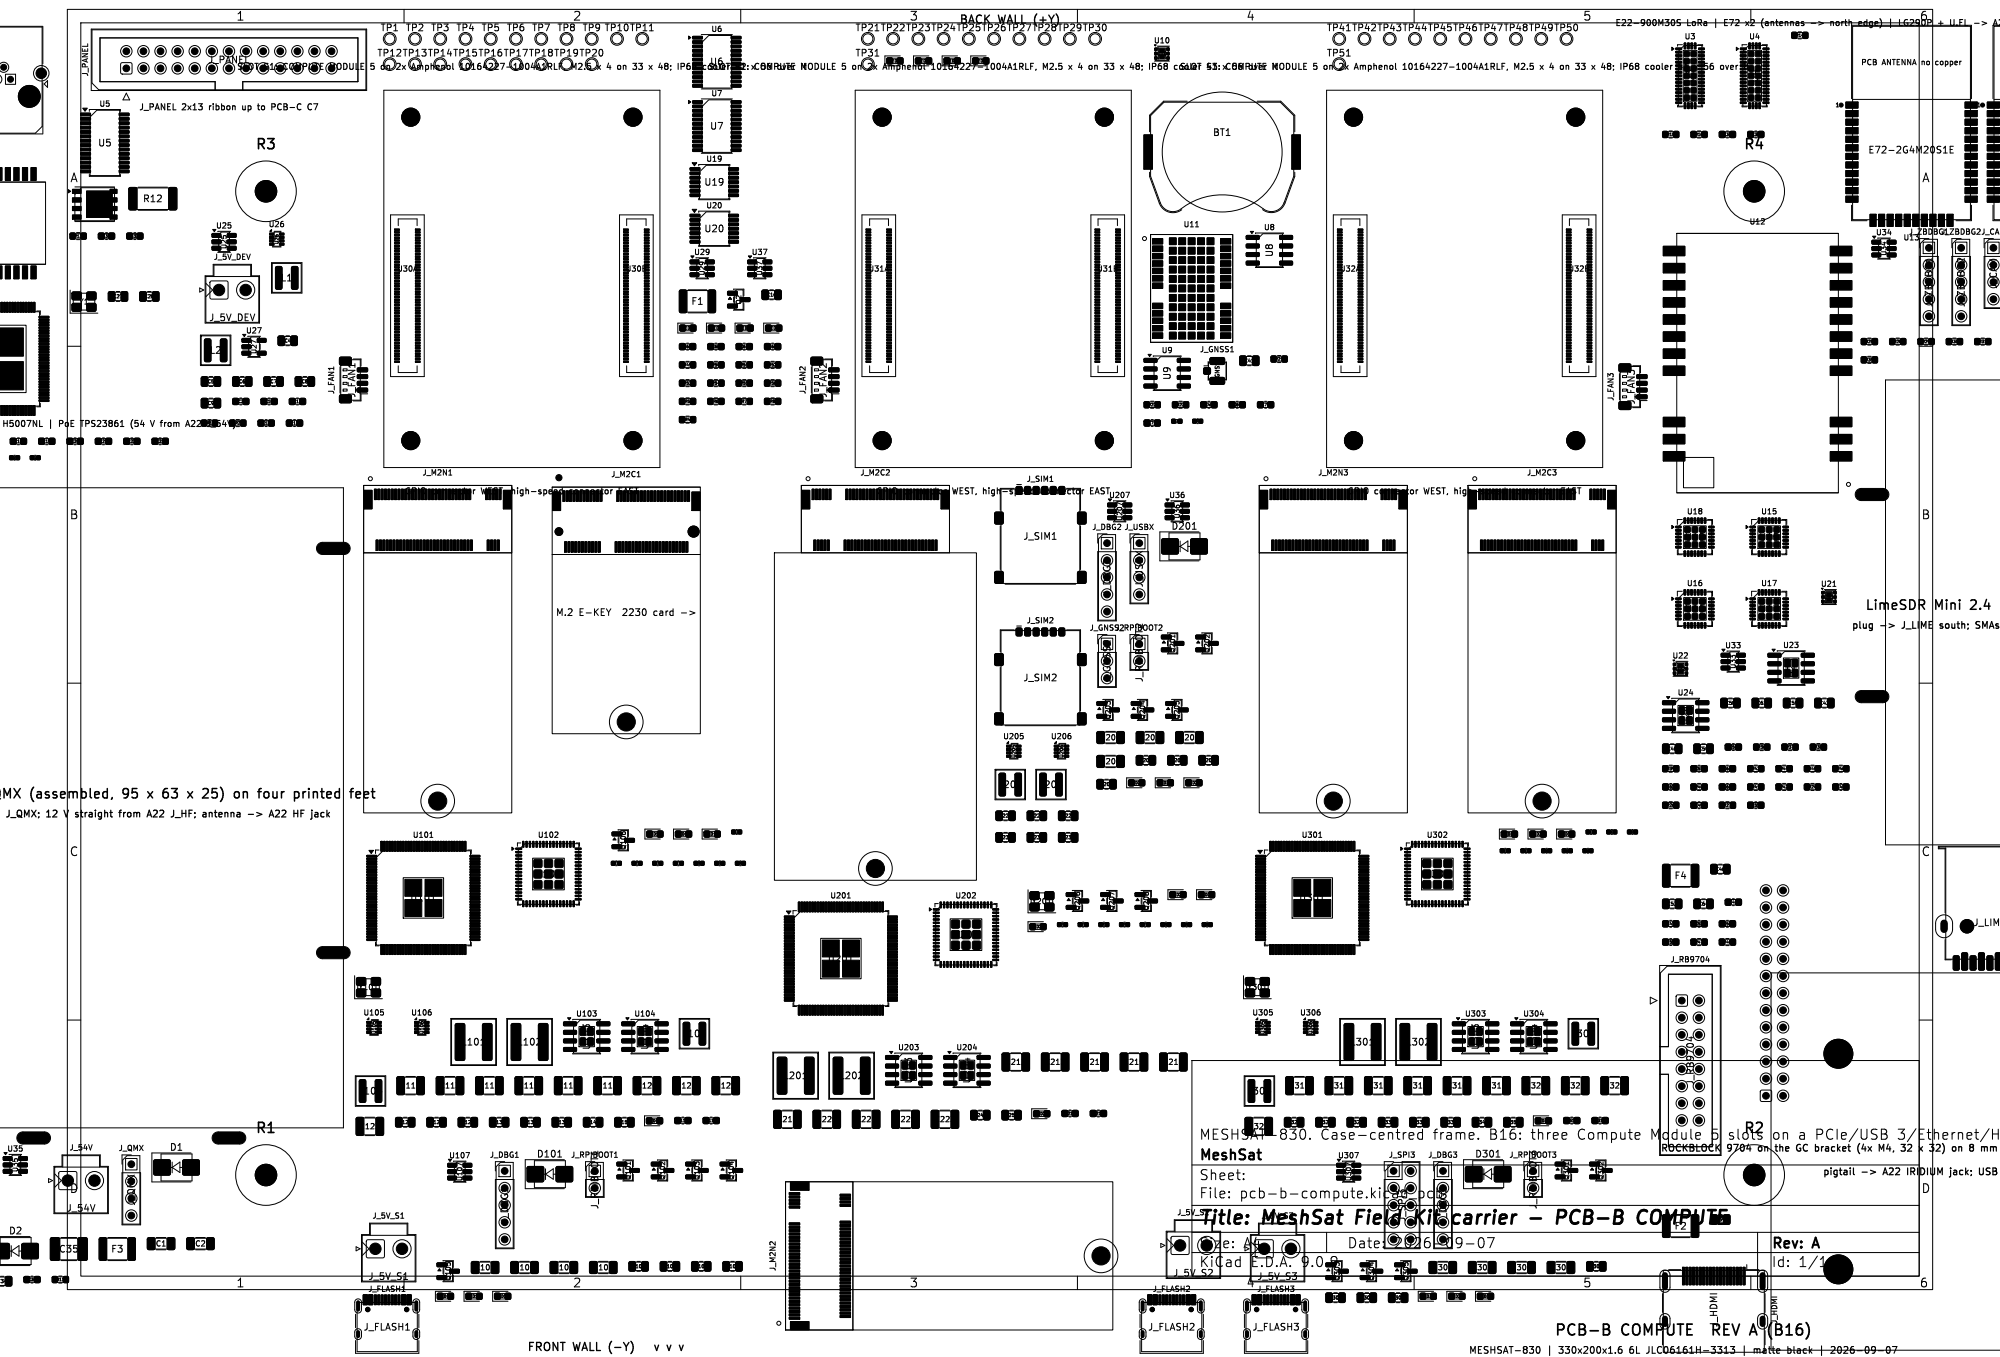
[picture p248: page 1]

PCB ANTENNA no copper 1

Id: 1/1 Title: MeshSat Field Kit carrier - PCB-B COMPUTE
