meshsat/meshsat-fieldkit/v2/release/revA/review/PCB-C-DISPLAY-C7/pcb-c-display-assembly-bottom-mirrored.pdf

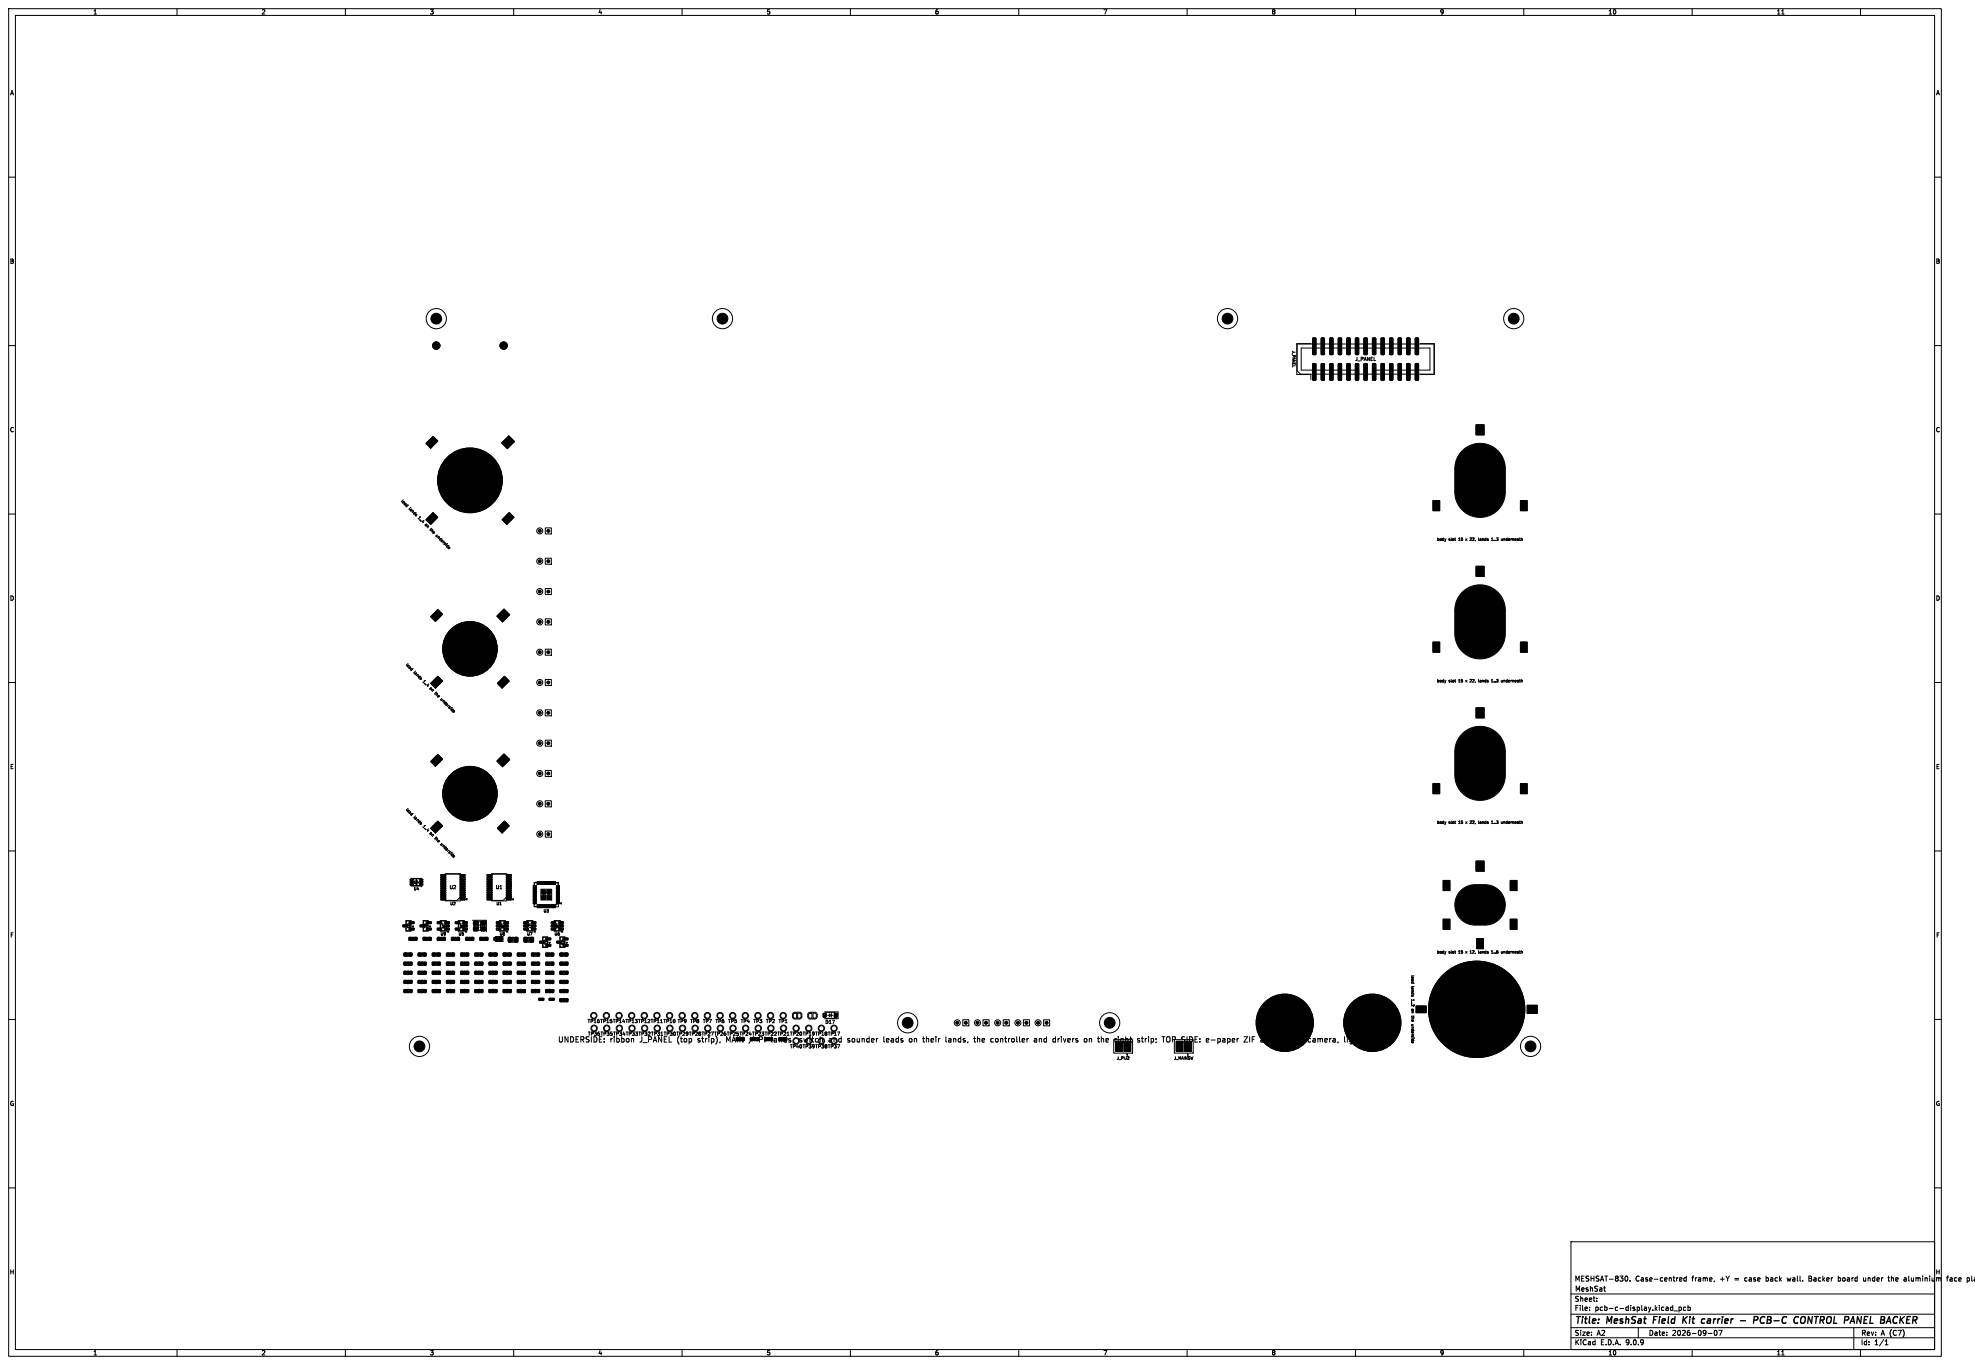
[picture p249: page 1]

body slot 15 x 22, lands 1..3 underneath
body slot 15 x 22, lands 1..3 underneath lead lands 1..2 on the underside

body slot 15 x 12, lands 1..6 underneath
