meshsat/meshsat-fieldkit/v2/release/revA/review/PCB-D-APRS-D8/pcb-d-aprs-assembly-bottom-mirrored.pdf

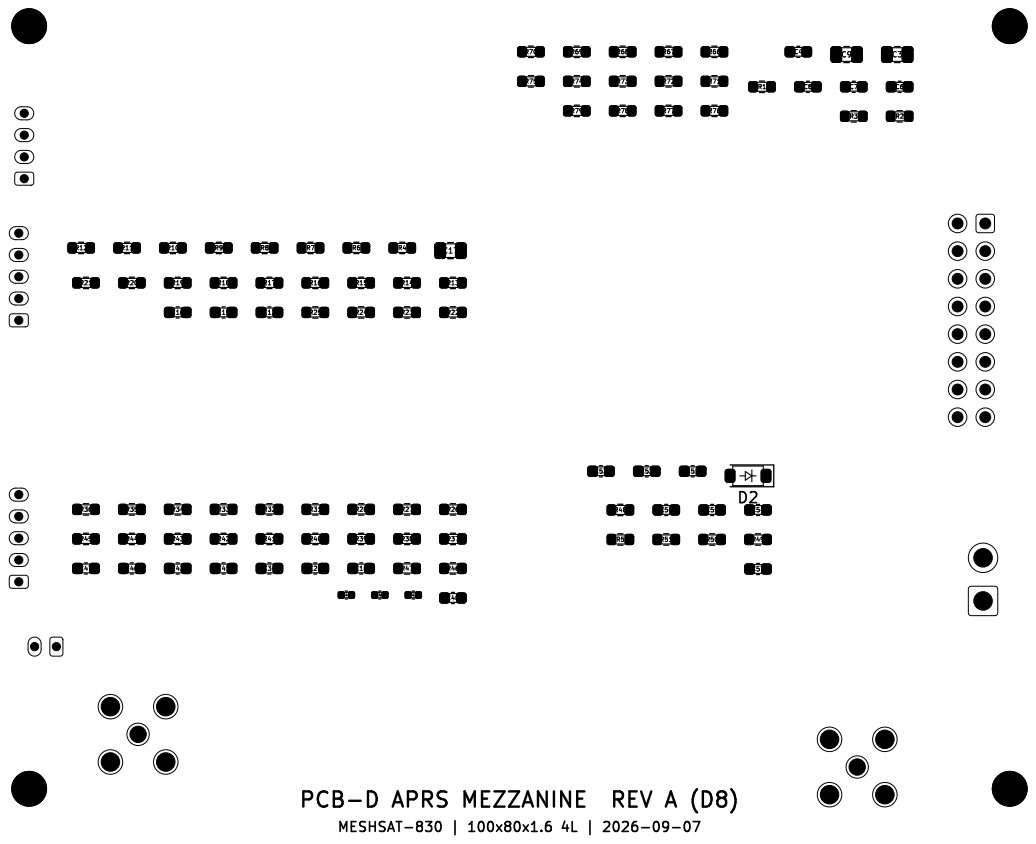
[picture p250: page 1]

Id: 1/1 Title: MeshSat Field Kit carrier - PCB-D APRS MEZZANINE
