meshsat/meshsat-fieldkit/v2/release/revA/review/PCB-P-PACK-P1/pcb-p-pack-assembly-bottom-mirrored.pdf

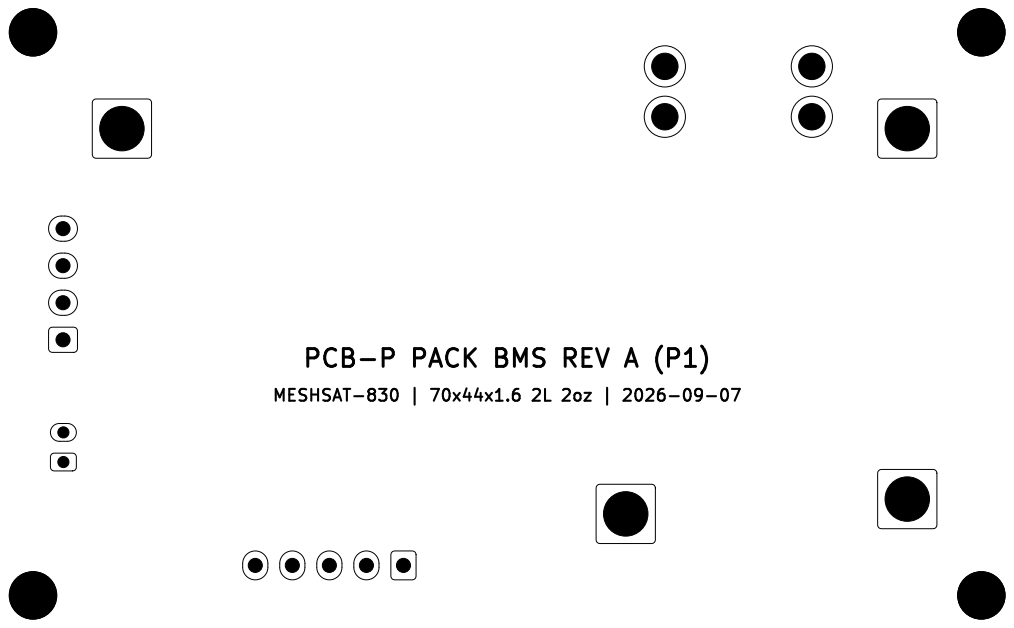
[picture p252: page 1]

Id: 1/1 Title: MeshSat Field Kit carrier - PCB-P PACK BMS
