meshsat/meshsat-fieldkit/v2/release/revA/review/PCB-P-PACK-P1/pcb-p-pack-assembly-top.pdf

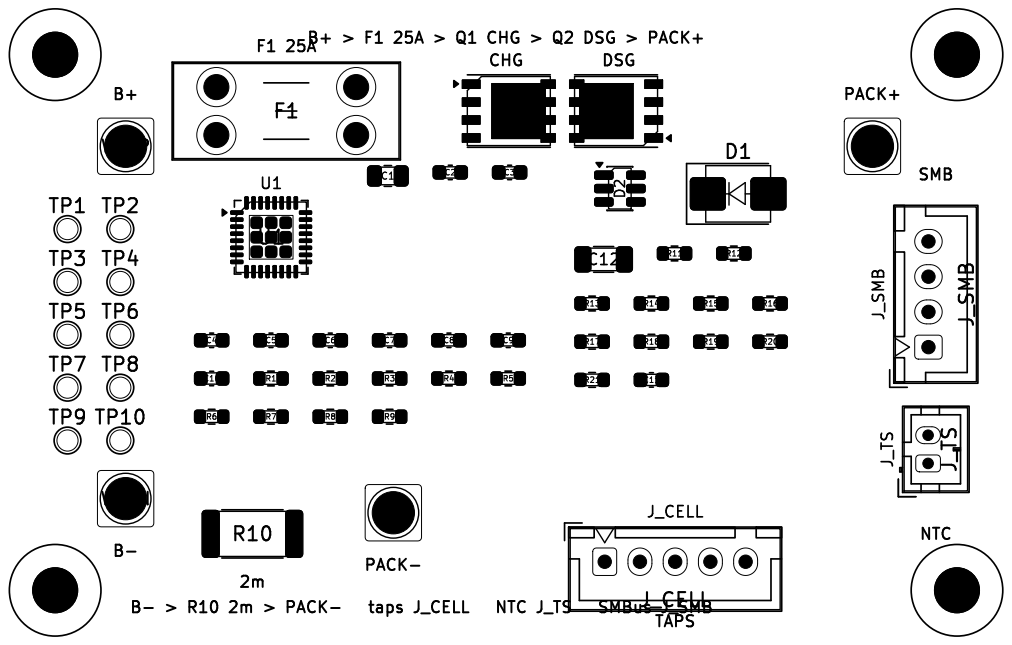
[picture p253: page 1]

Id: 1/1 Title: MeshSat Field Kit carrier - PCB-P PACK BMS
