meshsat/meshsat-fieldkit/v2/release/revA/review/PCB-A-POWER-A22/pcb-a-power-schematic.pdf

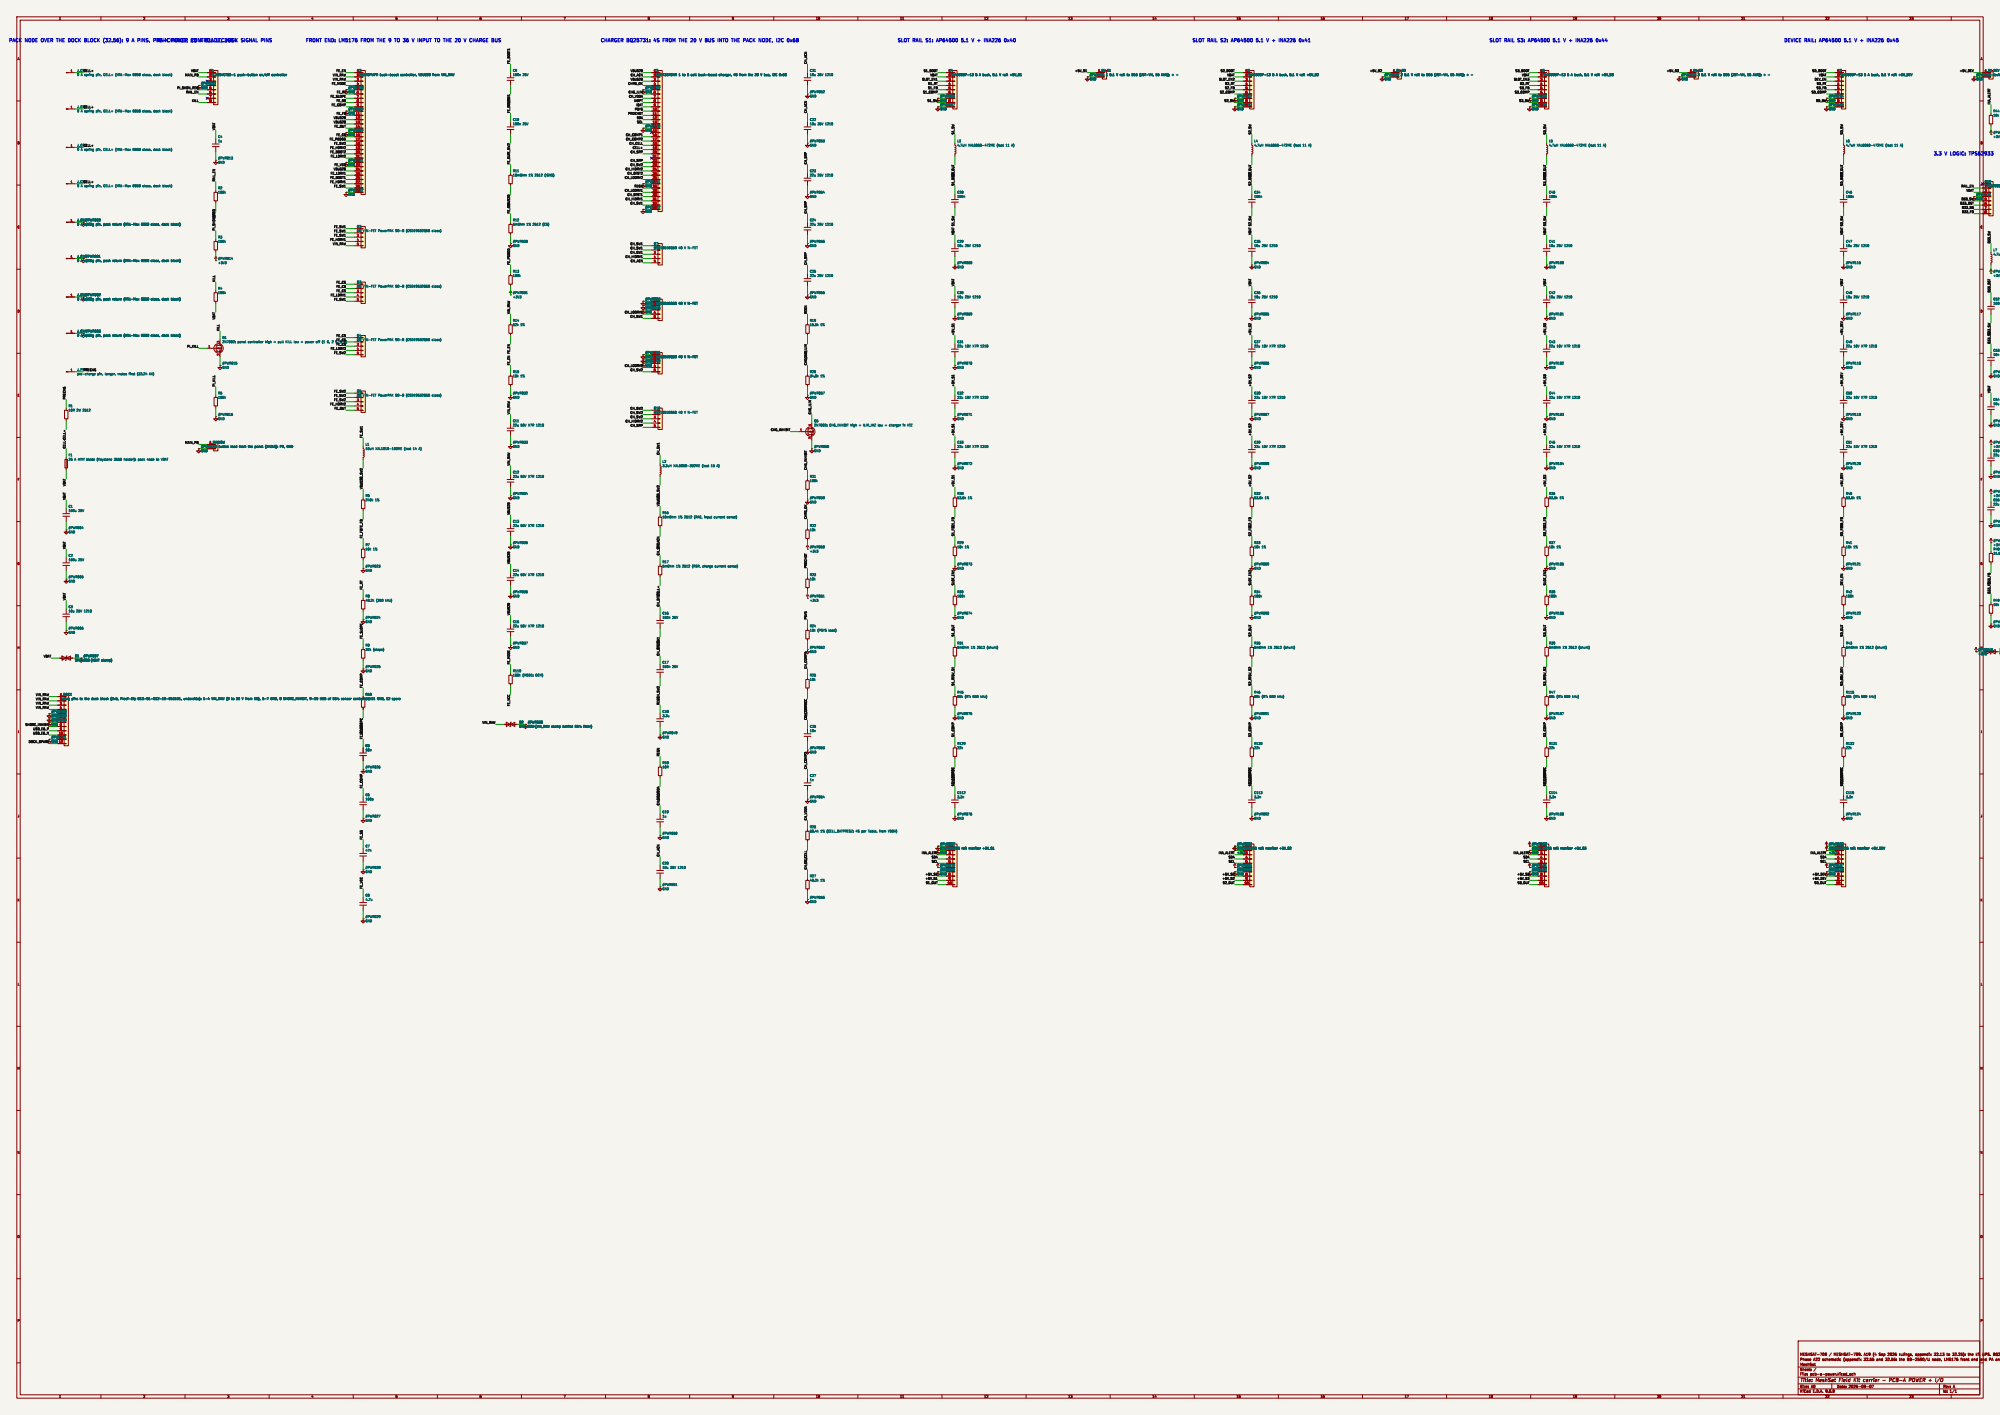
[picture p254: page 1]

100 V N-FET PowerPAK SO-8 (CSD19536KTT class) R7

J_MAINSW
MAIN button lead from the panel (XH2.5): PB, GND

10mOhm 1% 2512 (RAC, input current sense) R17

5mOhm 1% 2512 (RSR, charge current sense)

60.4k 1% (CELL_BATPRESZ: 4S per Table, from VDDA)

Id: 1/1 Title: MeshSat Field Kit carrier - PCB-A POWER + I/O
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
