meshsat/meshsat-fieldkit/v2/release/revA/review/PCB-P-PACK-P1/pcb-p-pack-schematic.pdf

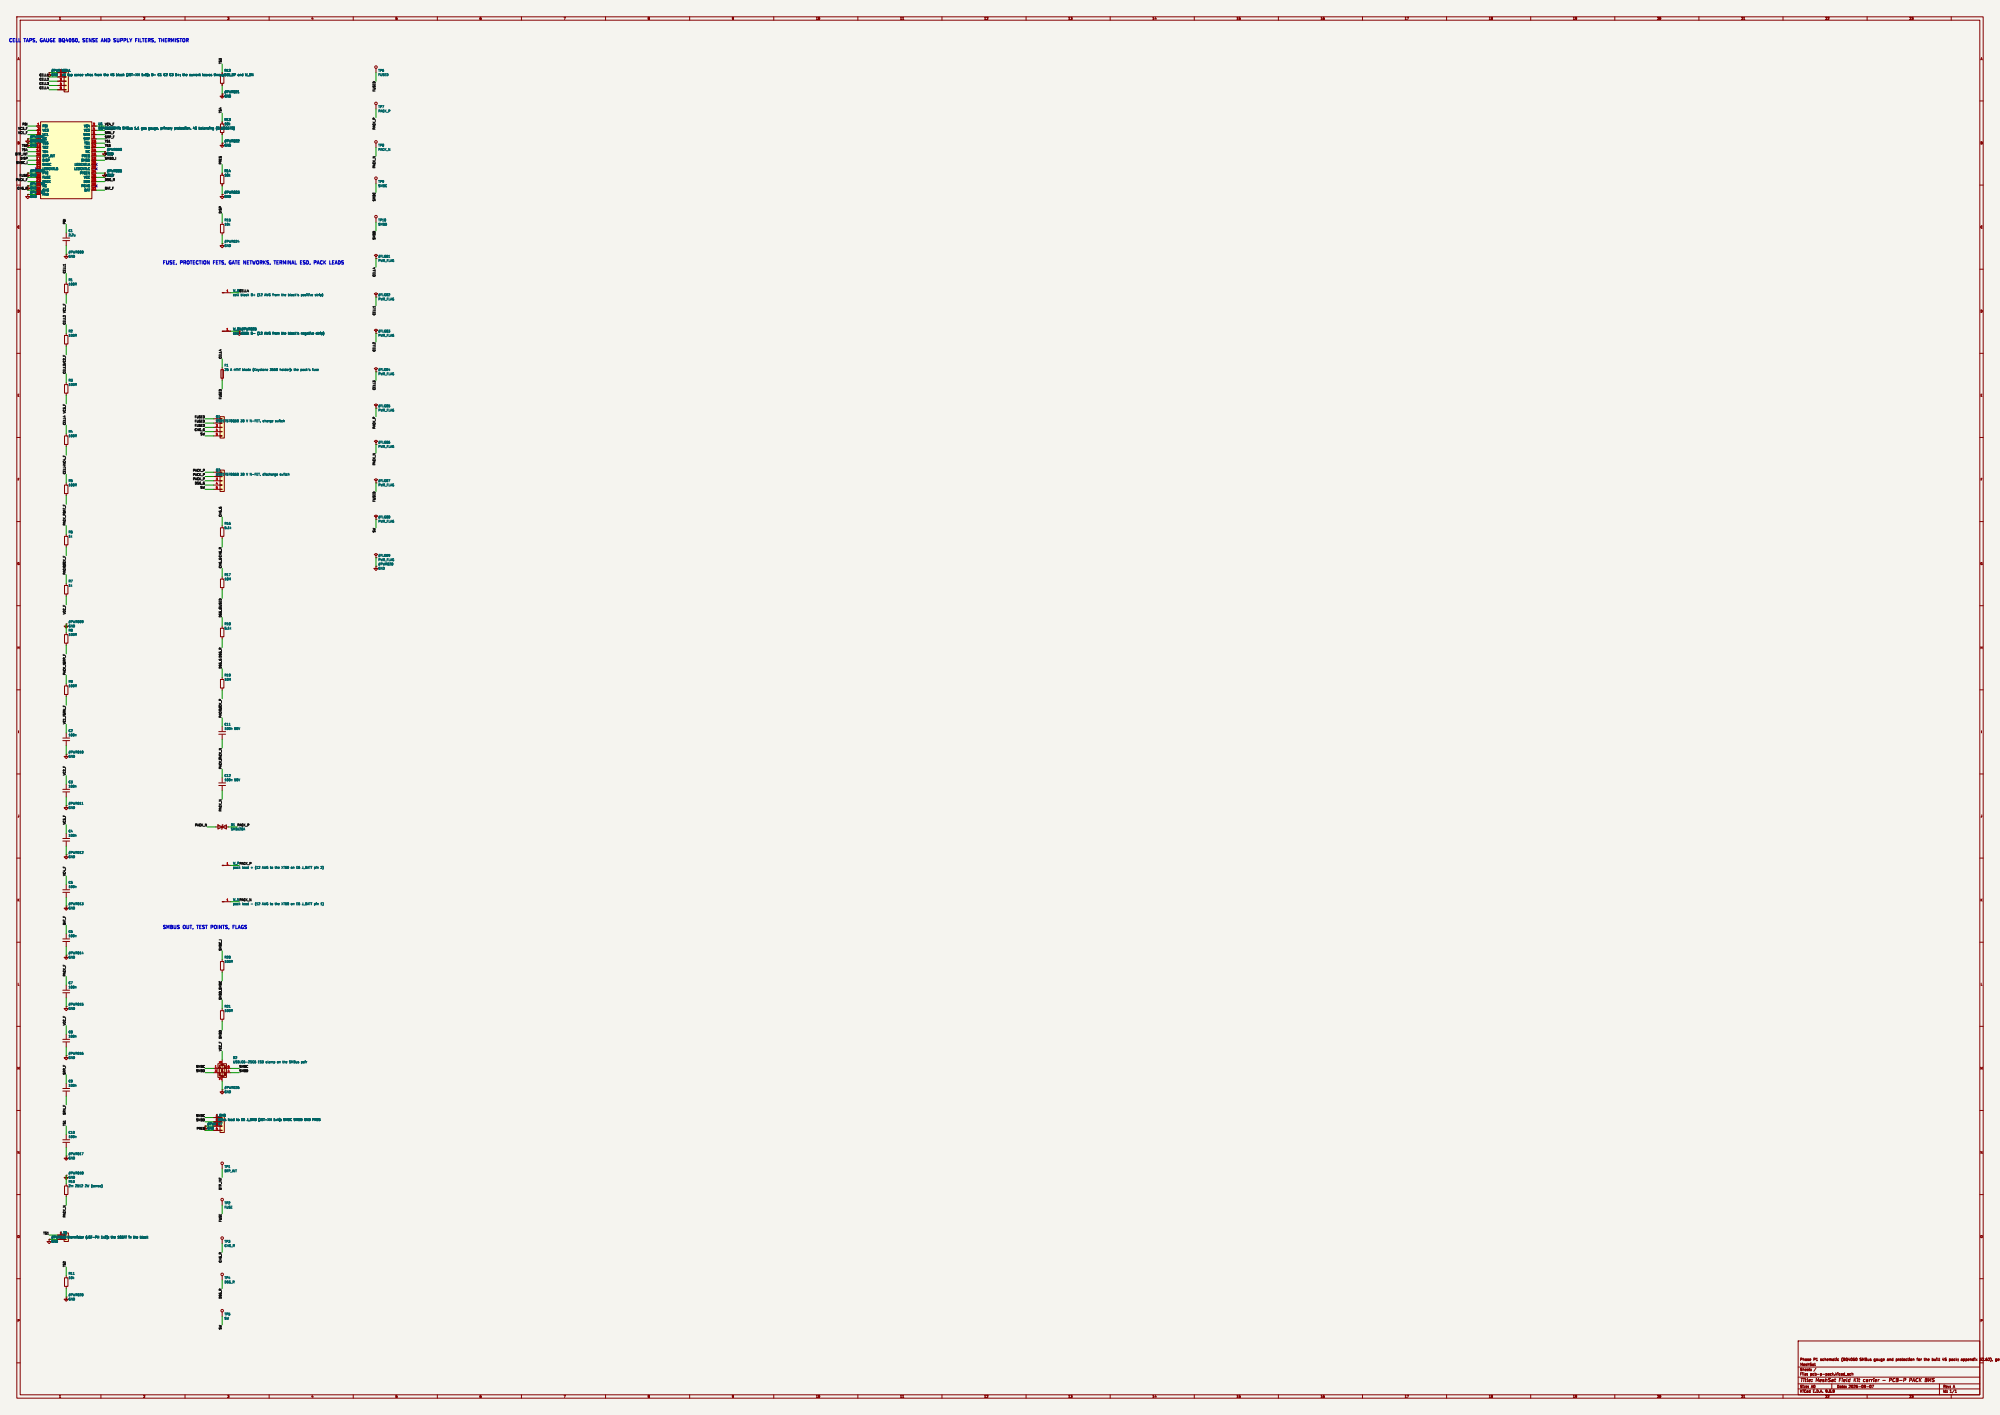
[picture p255: page 1]

CELL TAPS, GAUGE BQ4050, SENSE AND SUPPLY FILTERS, THERMISTOR

LEDCNTLA 20
LEDCNTLC 22 PTCEN 24 VCC 26 DSG 28 PCHG 30 BAT 32

FUSE, PROTECTION FETS, GATE NETWORKS, TERMINAL ESD, PACK LEADS

PACK_P
pack lead + (12 AWG to the XT60 on E6 J_BATT pin 2)

PACK_N
pack lead - (12 AWG to the XT60 on E6 J_BATT pin 1)

SMBUS OUT, TEST POINTS, FLAGS

Id: 1/1 Title: MeshSat Field Kit carrier - PCB-P PACK BMS
