meshsat/meshsat-fieldkit/v2/release/revA/review/PCB-C-DISPLAY-C7/pcb-c-display-schematic.pdf

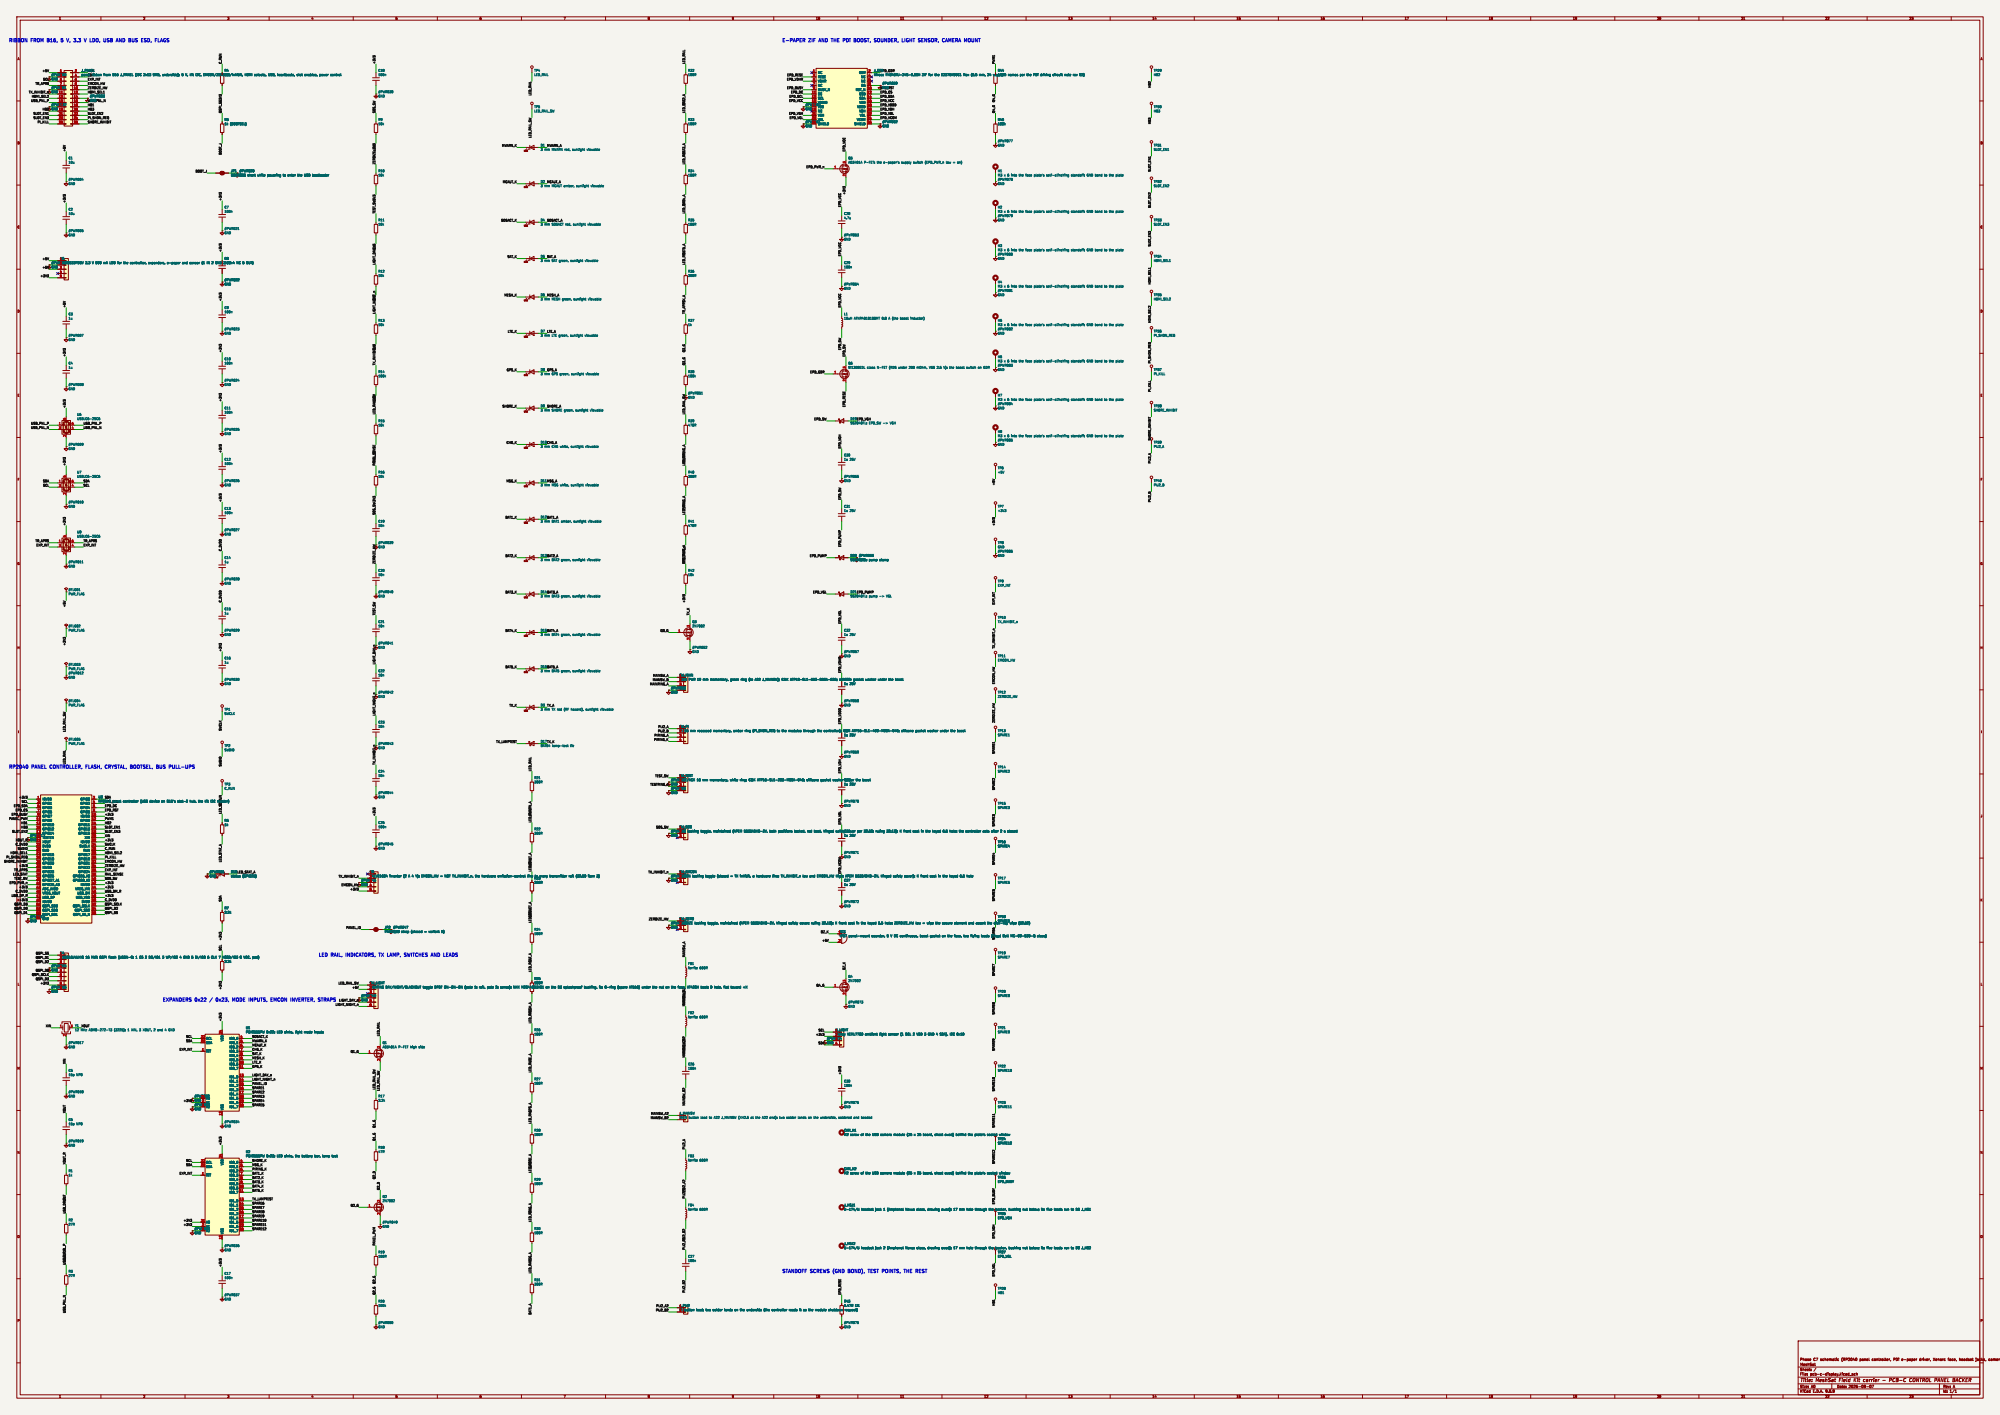
[picture p256: page 1]

NC 1 RESE 3 VDHR 5 NC 7 BUSY_N 9 DC

JP1 BOOTSEL: short while powering to enter the USB bootloader R5

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

U_LIGHT Vishay VEML7700 ambient light sensor (1 SCL 2 VDD 3 GND 4 SDA), I2C 0x10 1234 SW_ZERO

LED RAIL, INDICATORS, TX LAMP, SWITCHES AND LEADS

EXPANDERS 0x22 / 0x23, MODE INPUTS, EMCON INVERTER, STRAPS
LIGHT_NIGHT_n SPARE1 SPARE2 SPARE3 SPARE4 SPARE5 MESH_K MCAUT_K CHG_K

IO1_7 20 U1PCA9555PW 0x22: LED sinks, light mode inputs #PWR033 GND

STANDOFF SCREWS (GND BOND), TEST POINTS, THE REST

Id: 1/1 Title: MeshSat Field Kit carrier - PCB-C CONTROL PANEL BACKER
