meshsat/meshsat-fieldkit/v2/release/revA/review/PCB-E1-DOCK-E6/pcb-e1-dock-schematic.pdf

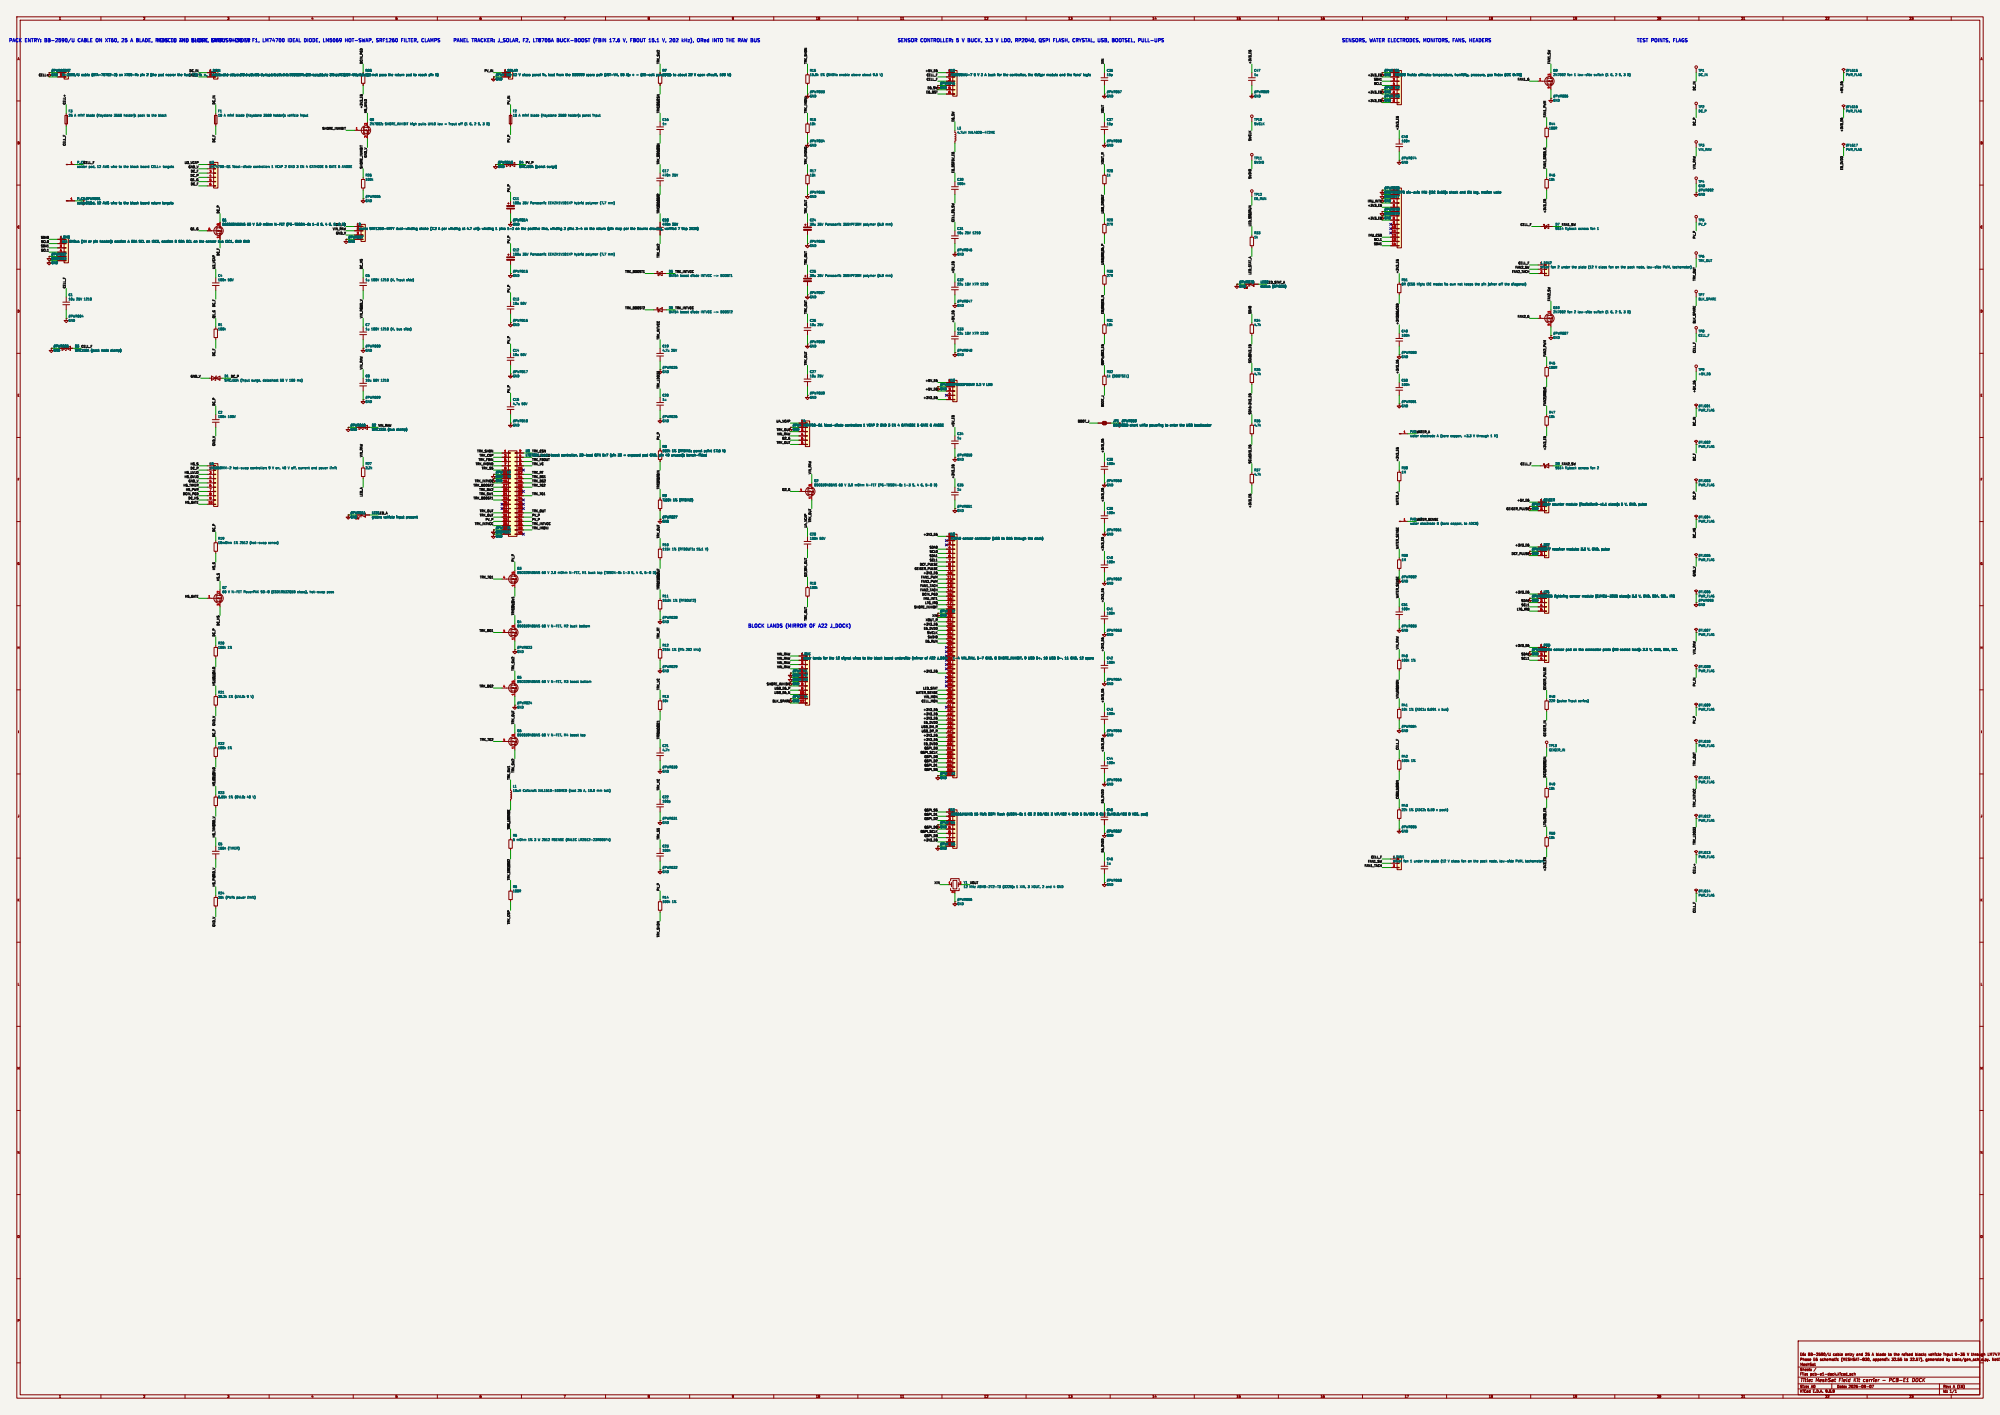
[picture p257: page 1]

IMU_INT1 CELL_F
solder pad, 12 AWG wire to the block board return targets 1

5 1 Q1 BSC039N06NS 60 V 3.9 mOhm N-FET (PG-TDSON-8: 1-3 S, 4 G, 5-8 D)

J_SMB
pack SMBus (XH or pin header): section A SDA SCL on I2C0, section B SDA SCL on the sensor bus I2C1, GND GND
#PWR002 GND
#PWR003 GND

#PWR002 GND #PWR003 GND

D3SMCJ18A (pack node clamp) #PWR004 GND

D3SMCJ18A (pack node clamp) #PWR005 GND

5 1 Q2 BSC039N06NS 60 V 3.9 mOhm N-FET (PG-TDSON-8: 1-3 S, 4 G, 5-8 D) #PWR039 GND

JP1 BOOTSEL: short while powering to enter the USB bootloader #PWR060 GND

JP1 BOOTSEL: short while powering to enter the USB bootloader #PWR059 GND

green: vehicle input present

J_DCF DCF77 receiver module: 3.3 V, GND, pulse
+3V3_E6 SDA1 +3V3_E6

5 1 Q3 BSC028N06NS 60 V 2.8 mOhm N-FET, M1 buck top (TDSON-8: 1-3 S, 4 G, 5-8 D) #PWR028 GND

BLOCK LANDS (MIRROR OF A22 J_DOCK)
