meshsat/meshsat-fieldkit/v2/release/revA/review/PCB-D-APRS-D8/pcb-d-aprs-schematic.pdf

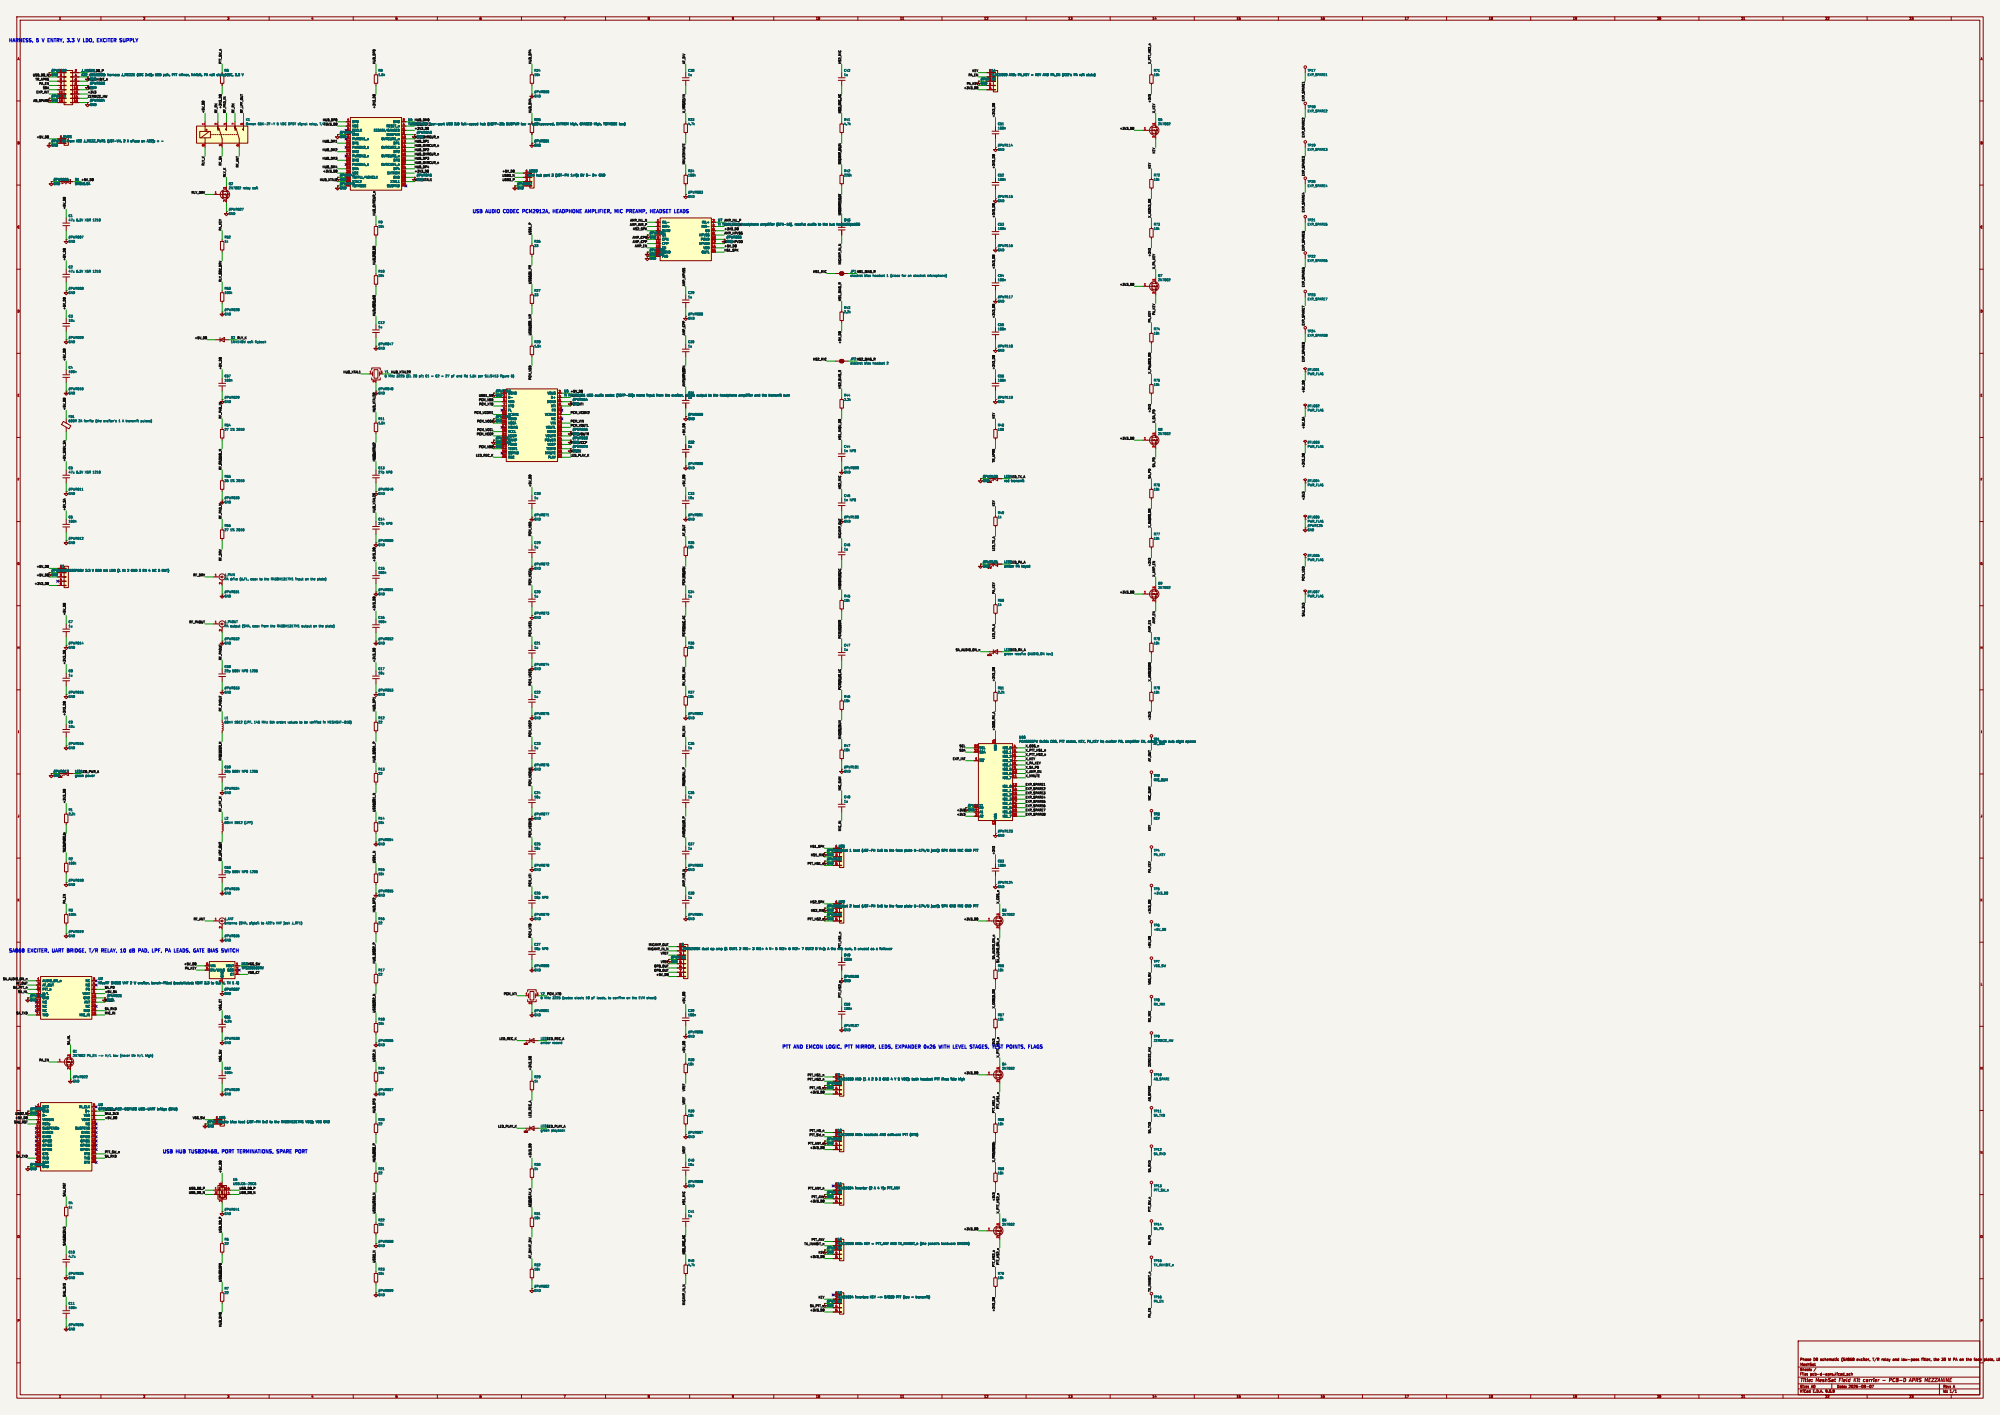
[picture p258: page 1]

HARNESS, 5 V ENTRY, 3.3 V LDO, EXCITER SUPPLY

TP17 EXP_SPARE1 12345U14
74LVC1G08 AND: PA_KEY = KEY AND PA_EN (A22's PA rail state) 12345
74LVC1G08 AND: PA_KEY = KEY AND PA_EN (A22's PA rail state)

USB AUDIO CODEC PCM2912A, HEADPHONE AMPLIFIER, MIC PREAMP, HEADSET LEADS

#PWR012 GND 12345U1 TLV75533PDBV 3.3 V 500 mA LDO (1 IN 2 GND 3 EN 4 NC 5 OUT) C7

U1 TLV75533PDBV 3.3 V 500 mA LDO (1 IN 2 GND 3 EN 4 NC 5 OUT) 12345
#PWR013 GND

SA868 EXCITER, UART BRIDGE, T/R RELAY, 10 dB PAD, LPF, PA LEADS, GATE BIAS SWITCH

PTT AND EMCON LOGIC, PTT MIRROR, LEDS, EXPANDER 0x26 WITH LEVEL STAGES, TEST POINTS, FLAGS

74LVC1G08 AND (1 A 2 B 3 GND 4 Y 5 VCC): both headset PTT lines idle high 12345
74LVC1G08 AND (1 A 2 B 3 GND 4 Y 5 VCC): both headset PTT lines idle high
PTT_HS2_n PTT_HS_n PTT_SW_n +3V3_D8 PTT_ANY_n

74LVC1G08 AND: headsets AND software PTT (RTS) 12345
74LVC1G08 AND: headsets AND software PTT (RTS)
#PWR109 GND

USB HUB TUSB2046B, PORT TERMINATIONS, SPARE PORT

74LVC1G08 AND: KEY = PTT_ANY AND TX_INHIBIT_n (the panel's hardware EMCON) 12345
74LVC1G08 AND: KEY = PTT_ANY AND TX_INHIBIT_n (the panel's hardware EMCON)
#PWR111 GND

Id: 1/1 Title: MeshSat Field Kit carrier - PCB-D APRS MEZZANINE
