meshsat/meshsat-fieldkit/v2/release/revA/boards/meshsat-pcb-b-revA-B14/pcb-b-compute-schematic.pdf

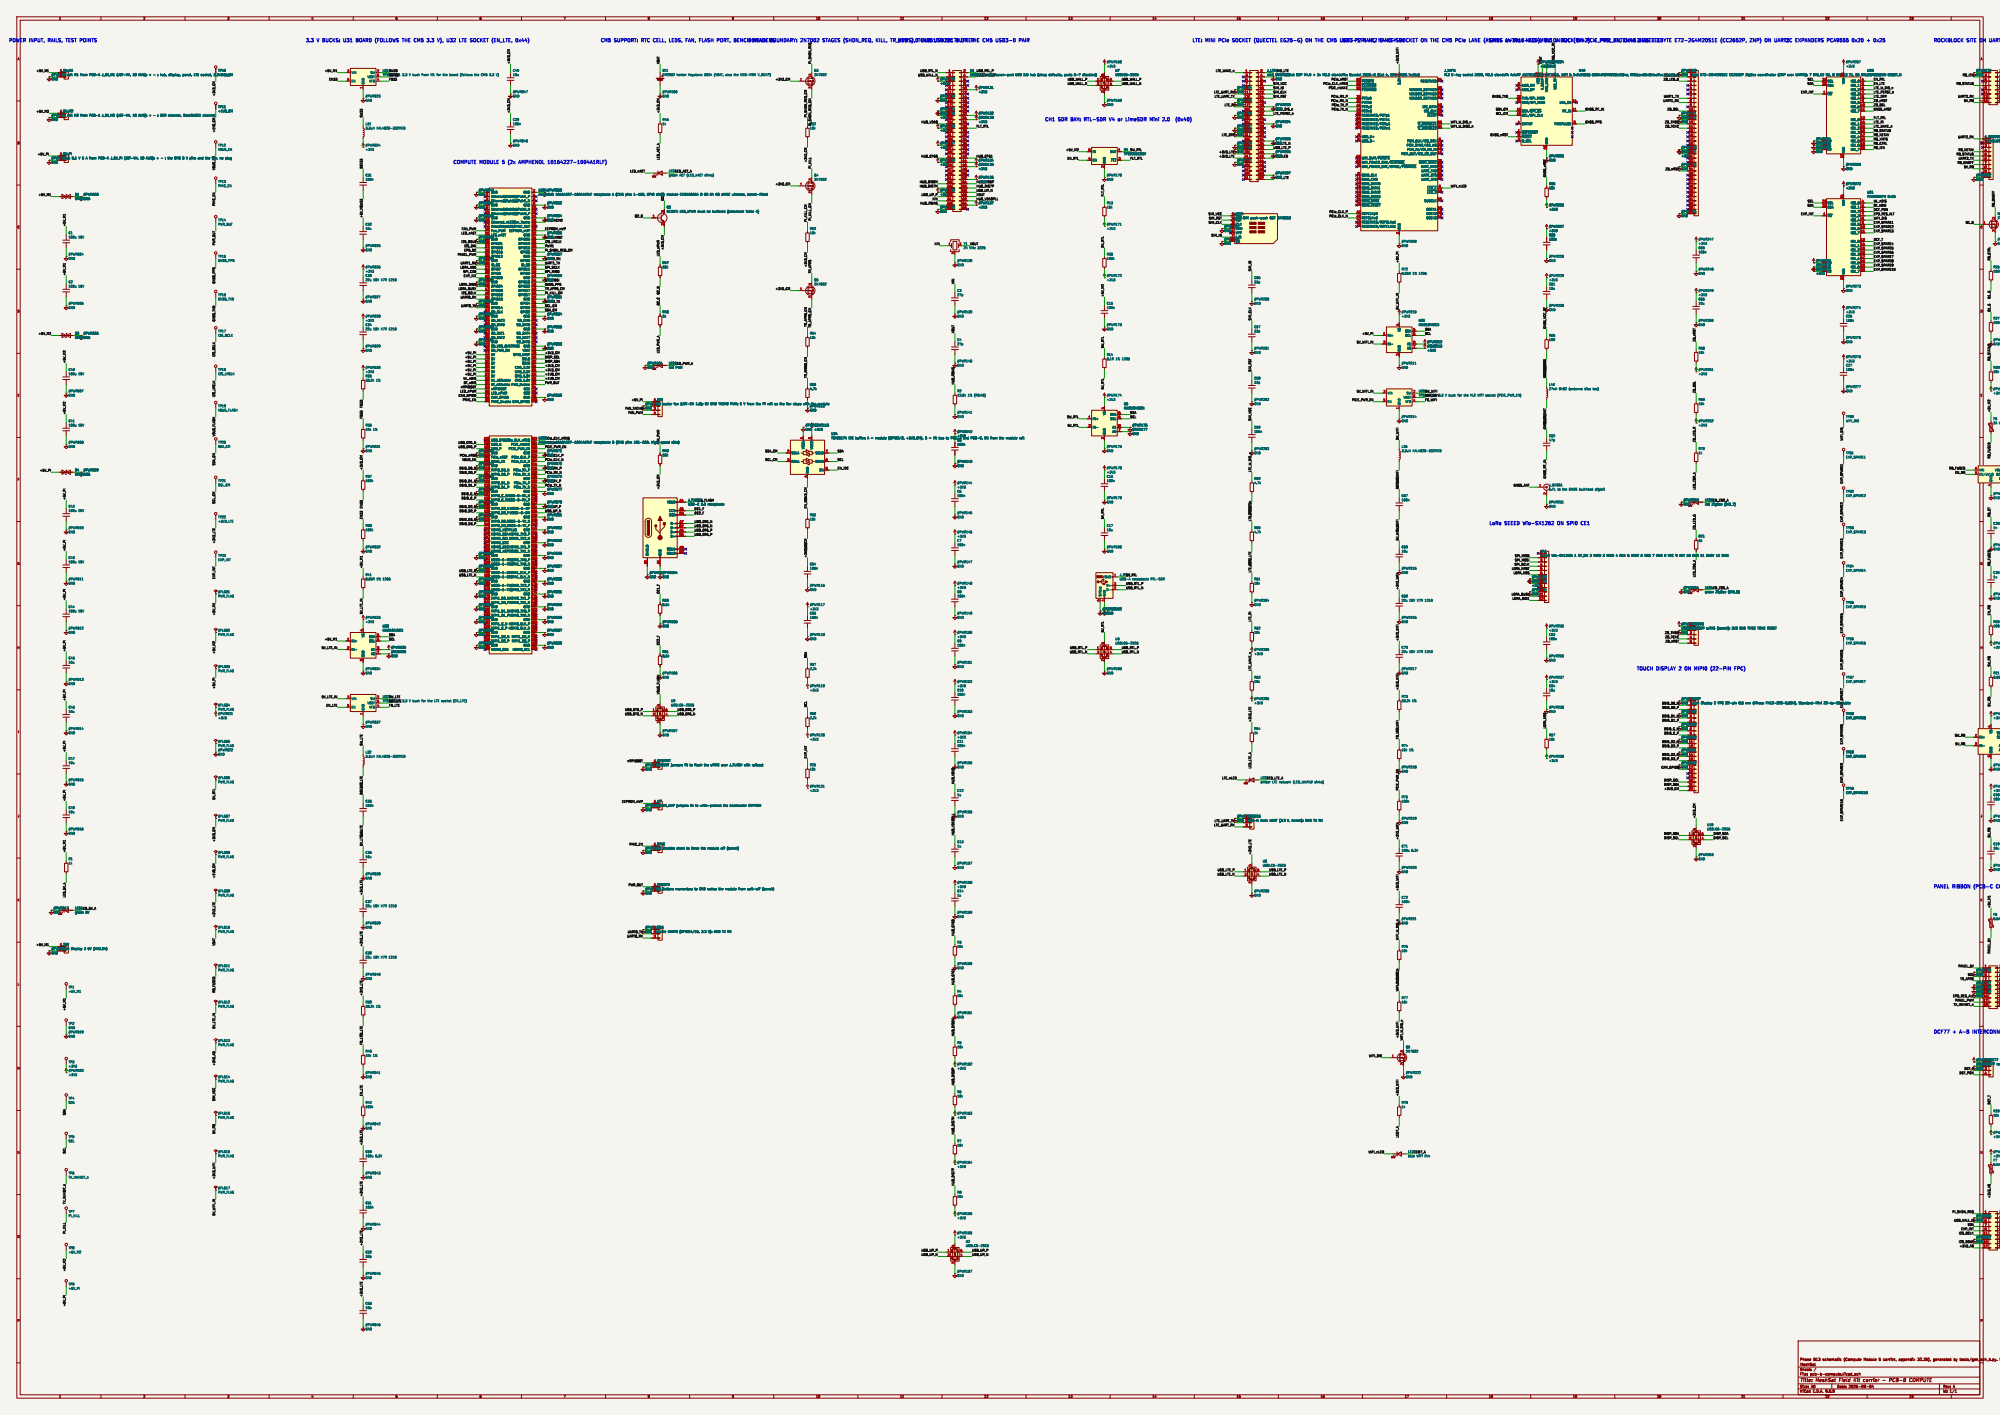
[picture p259: page 1]

1 SW 2 VBST 6 VFB 4 U31 TPS563201 3.3 V buck from M1 for the board (follows the CM5 3.3 V) #PWR283 GND

BT1 CR2032 holder Keystone 3034 (VBAT, also the NEO-M9N V_BCKP) #PWR047 GND

#PWR049 GND
#PWR066 GND GND 1 Ethernet_Pair3_P 3 Ethernet_Pair3_N 5 GND 7 Ethernet_Pair2_N 9 Ethernet_Pair2_P 11 GND 13 Ethernet_nLED3 15 Ethernet_nLED2 17 Fan_PWM 19

3 2 Q2 BC857: LED_nPWR must be buffered (datasheet Table 4) #PWR061 GND

LED_nACT 21 GND 23 GPIO21 25 GPIO20 27 GPIO16 29 GPIO12 31 GND 33
ID_SC 35 GPIO7 37 GPIO8 39 GPIO25 41 GND 43 GPIO24 45 GPIO23 47 GPIO18 49 GPIO15 51 GND 53 GPIO14 55 SD_CLK 57 GND 59 SD_DAT3 61 SD_DAT0 63 GND 65 SD_DAT1 67 SD_DAT2 69 GND 71 SD_VDD_OVERRIDE 73 SD_PWR_ON 75

#PWR057

#PWR057 GND
ID_SD 36 GPIO11 38 GPIO9 40 GND 42 GPIO10 44 GPIO22 46 GPIO27 48 GPIO17 50 GND 52 GPIO4 54 GPIO3 56 GPIO2 58 GND 60 SD_CMD 62 SD_DAT5 64 GND 66 SD_DAT4 68 SD_DAT7 70 SD_DAT6 72 GND 74 VBAT 76 GPIO_VREF 78 SCL0 80 SDA0 82 CM5_3.3V 84 CM5_3.3V 86 CM5_1.8V 88 CM5_1.8V 90 PWR_Button 92 CC1 94 CC2 96 GND 98 CAM_GPIO1 100

USB_OTG_ID 101 USB_N 103 USB_P 105 GND 107 PCIe_nRST 109 VBUS_EN 111 GND 113 MIPI0_D0_N 115 MIPI0_D0_P 117 GND 119 MIPI0_D1_N 121 MIPI0_D1_P 123 GND 125 MIPI0_C_N 127 MIPI0_C_P 129 GND 131 MIPI0_D2_N 133 MIPI0_D2_P 135 GND 137 MIPI0_D3_N 139 MIPI0_D3_P 141 HDMI1_HOTPLUG 143 HDMI1_SDA 145 HDMI1_SCL 147 HDMI1_CEC 149 HDMI0_CEC 151 HDMI0_HOTPLUG 153 GND 155 USB3-1-RX_N 157 USB3-1-RX_P 159 GND 161 USB3-1-DP 163 USB3-1-DM 165 GND 167 USB3-1-TX_N 169 USB3-1-TX_P 171 GND 173 MIPI1_D0_N 175 MIPI1_D0_P 177 GND 179 MIPI1_D1_N 181 MIPI1_D1_P 183 GND 185 MIPI1_C_N 187 MIPI1_C_P 189 GND 191 MIPI1_D2_N 193 MIPI1_D2_P 195 GND 197 HDMI0_SDA 199

1 SW 2 VBST 6 VFB 4 U32 TPS563201 3.3 V buck for the LTE socket (EN_LTE) C36

J_RPIBOOT
nRPIBOOT jumper: fit to flash the eMMC over J_FLASH with rpiboot 1

#PWR108 GND

LED2
amber LTE network (LED_WWAN# sinks)

J_PMIC
PMIC_Enable: short to force the module off (bench) 1

PMIC_Enable: short to force the module off (bench)

DCF77 + A-B INTERCONNECT 2x9 (I2S, GATED 3.3 V FOR THE CODEC)

Id: 1/1 Title: MeshSat Field Kit carrier - PCB-B COMPUTE
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
