meshsat/meshsat-fieldkit/v2/release/handover/H1/v2/release/handover/_generated/pcb-a-power-a23/pcb-a-power-schematic.pdf

J_CP4 | R¹⁵⁰
CELL_FUSED | PD_VCC

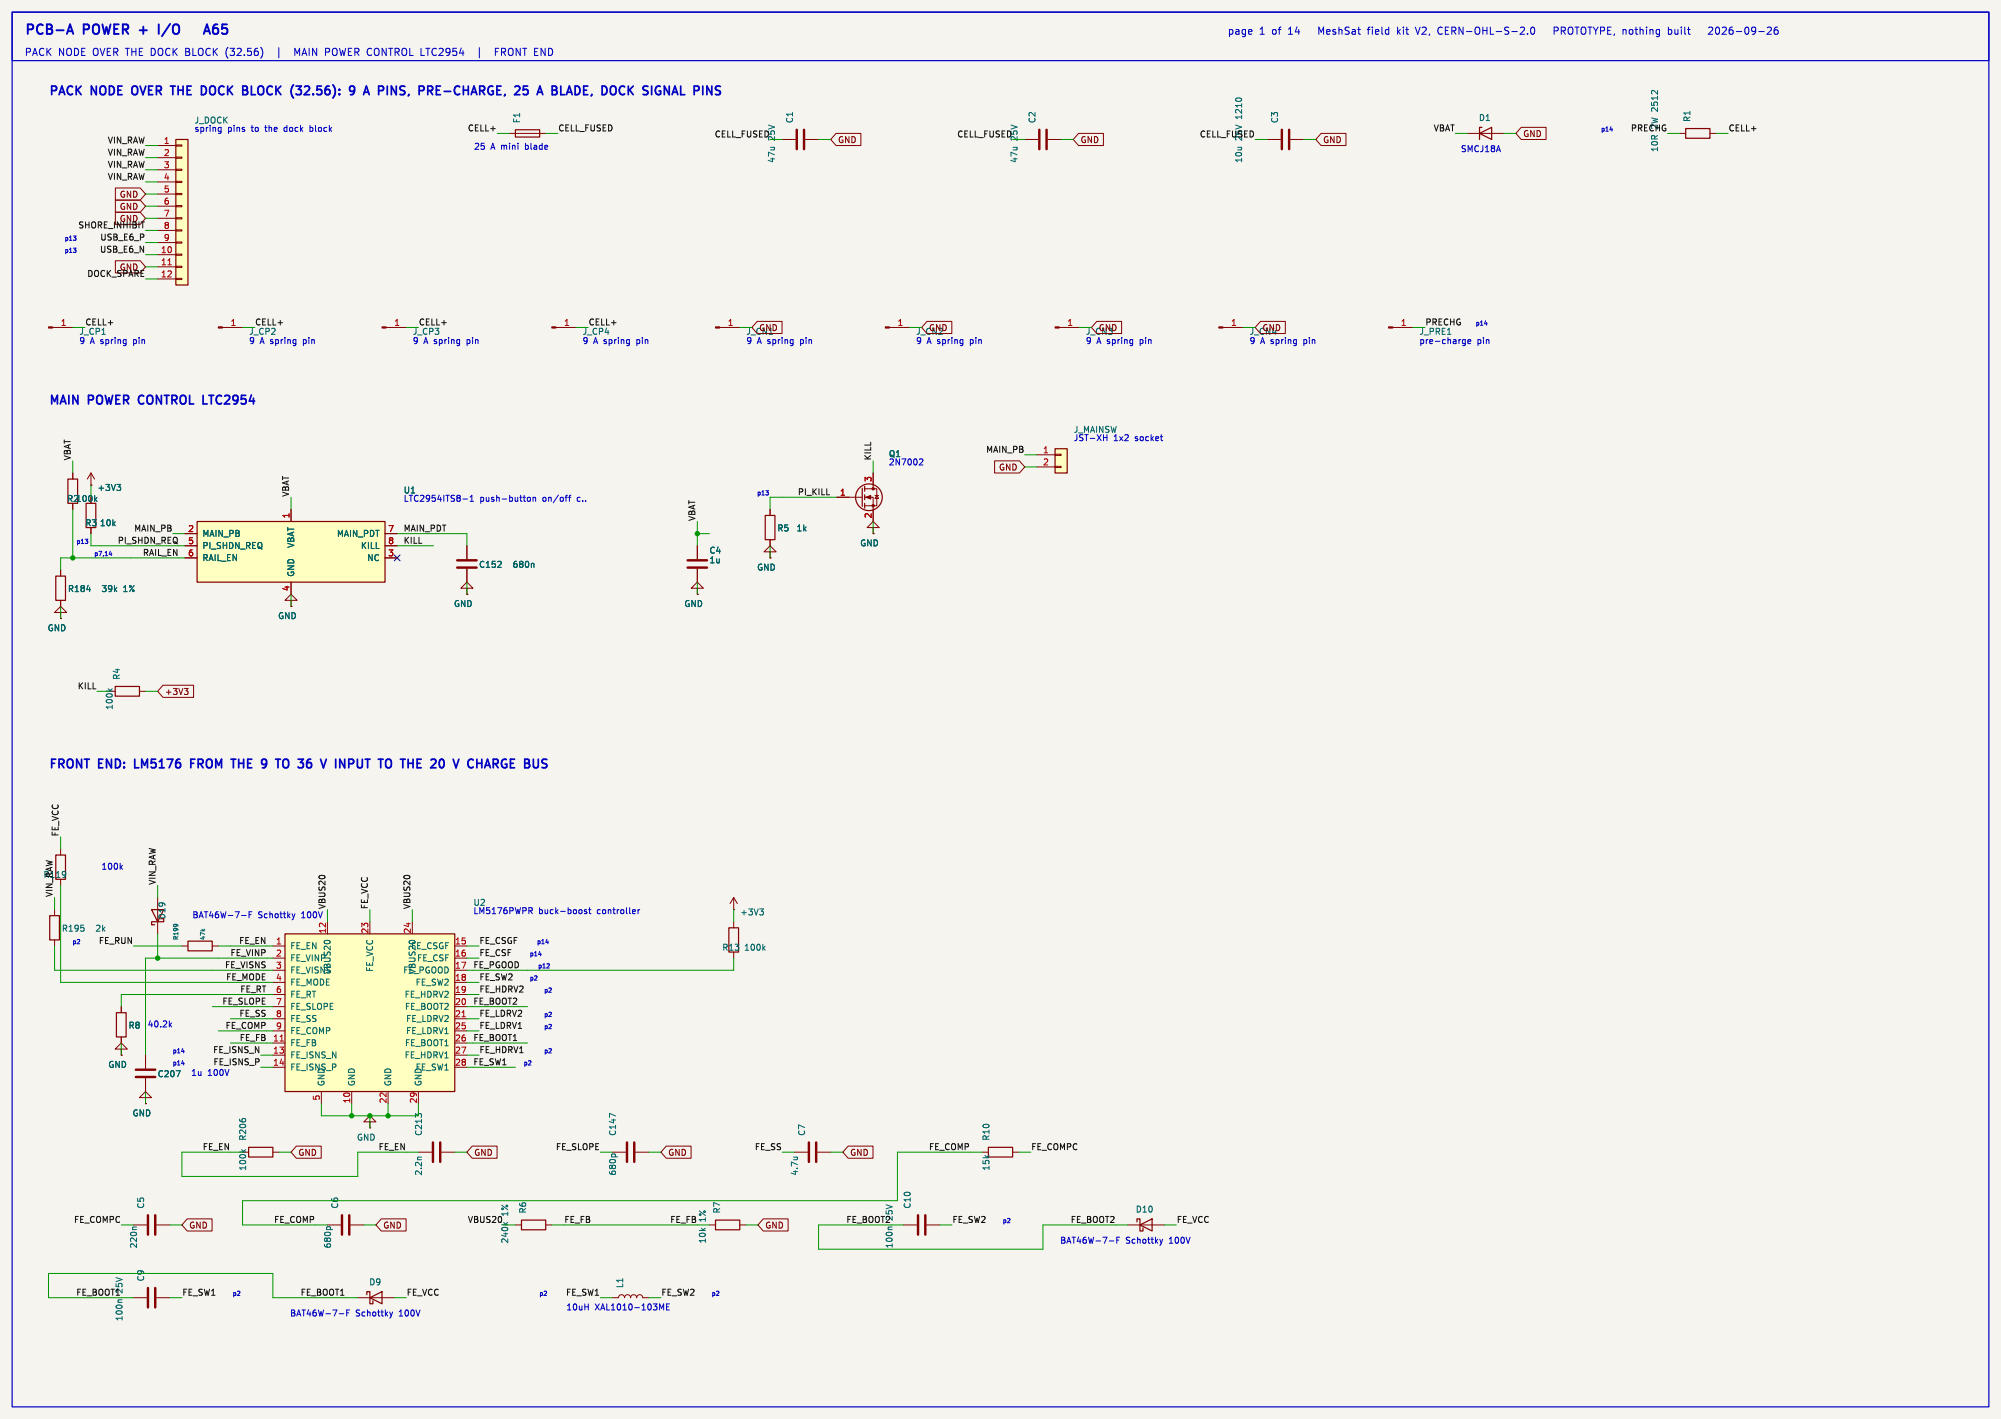
[picture p260: page 1]

J_DOCK
spring pins to the dock block

FRONT END: LM5176 FROM THE 9 TO 36 V INPUT TO THE 20 V CHARGE BUS

4 Q2
5 Q7 CSD18510Q5B | 40 V N-FET D² | +3V3

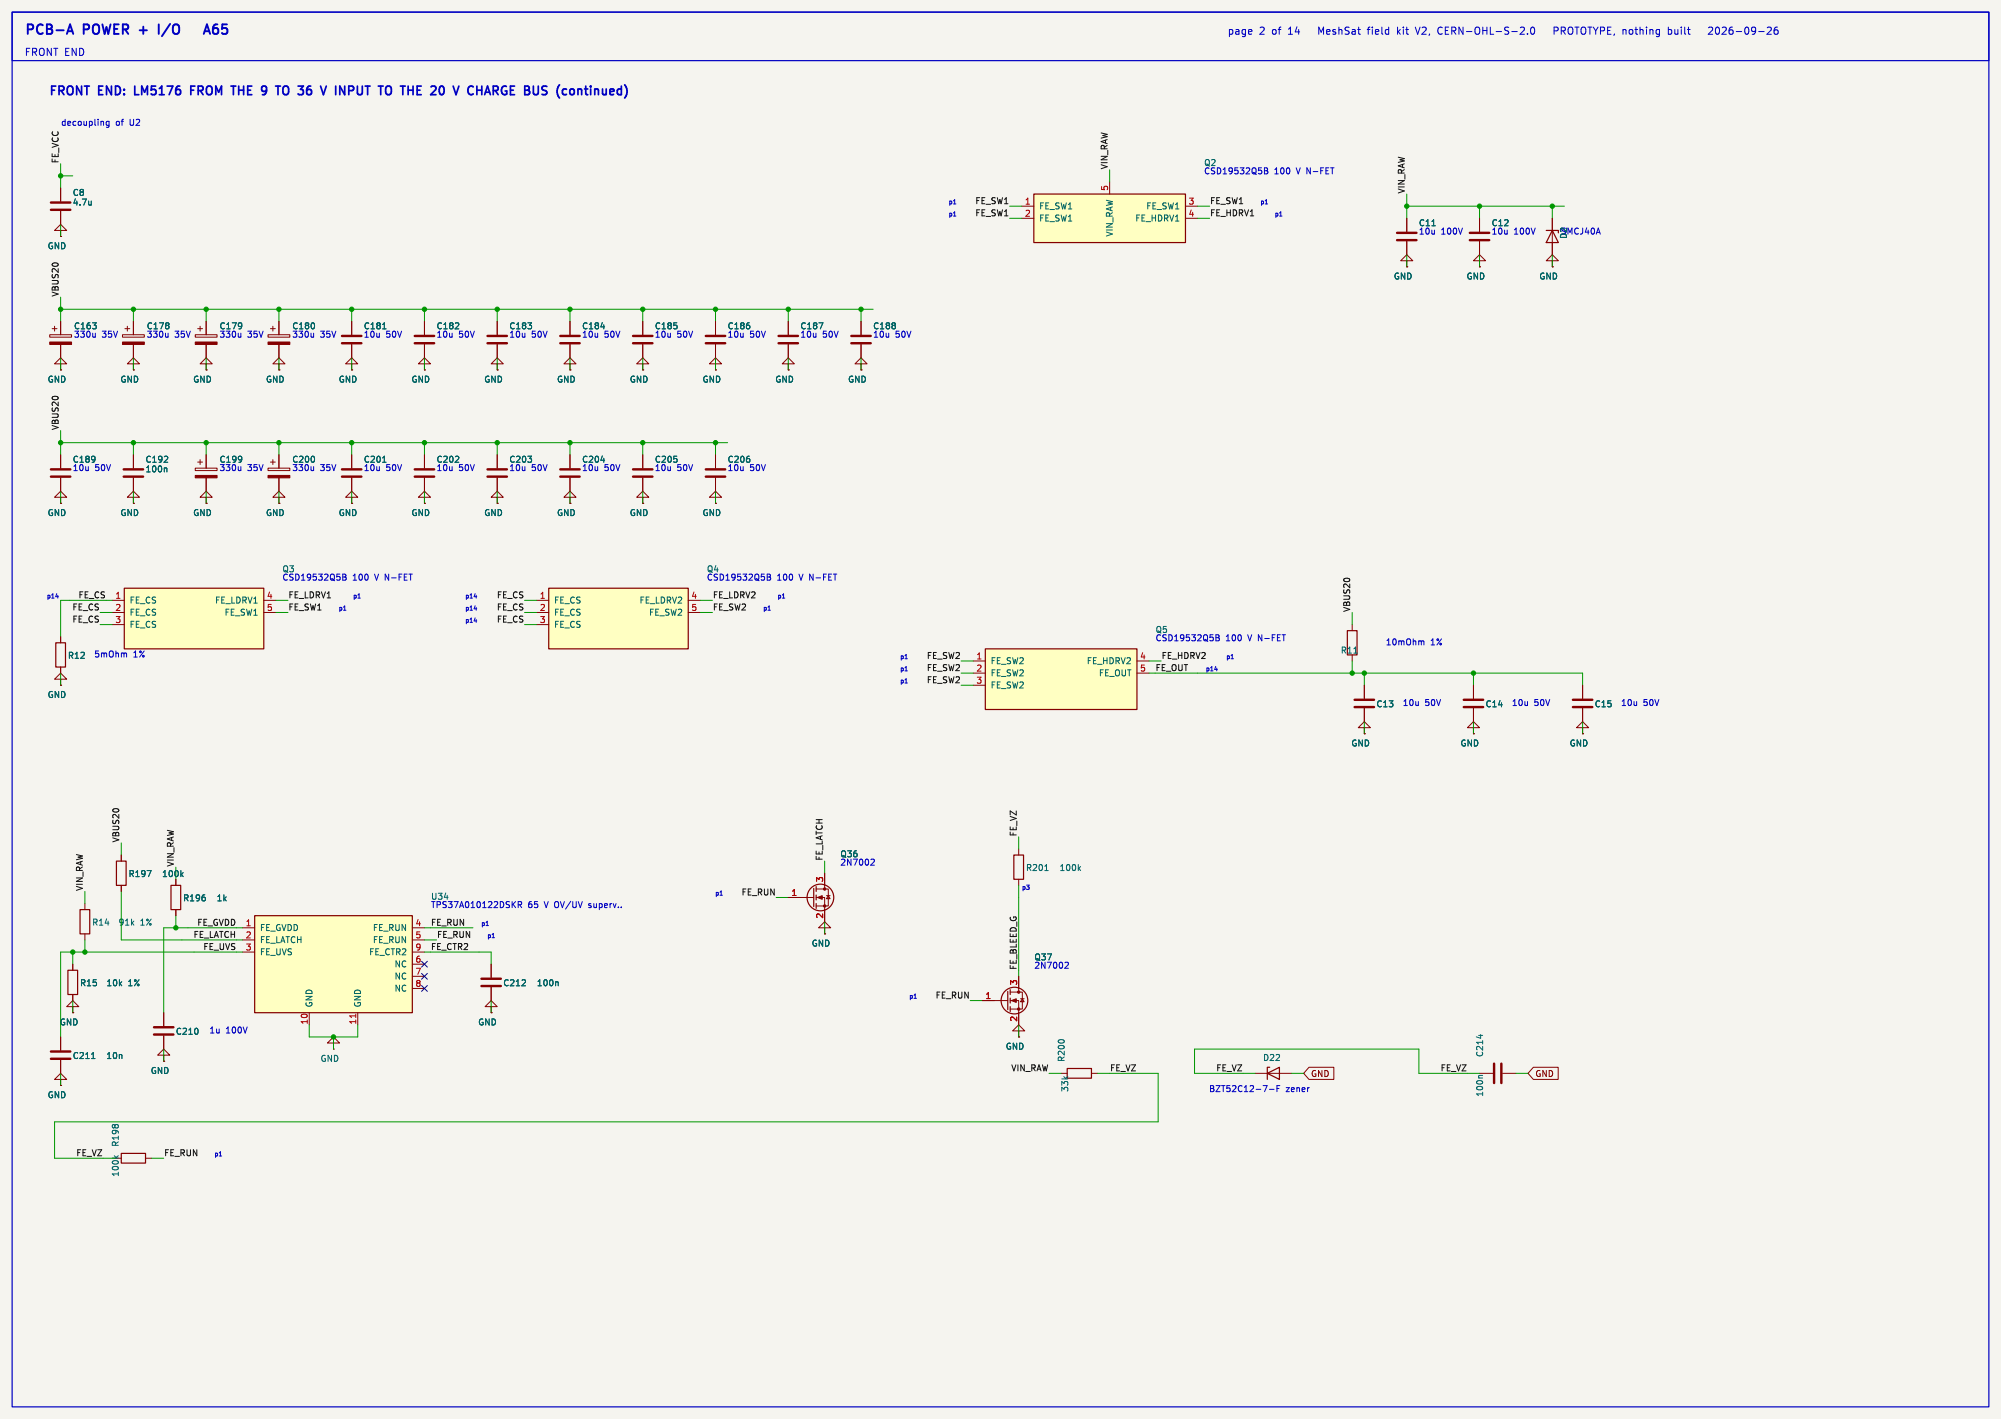
[picture p261: page 2]

FRONT END: LM5176 FROM THE 9 TO 36 V INPUT TO THE 20 V CHARGE BUS (continued)

5 Q7 CSD18510Q5B | 40 V N-FET D² | +3V3
FE_ISNS_P | VBUS²⁰

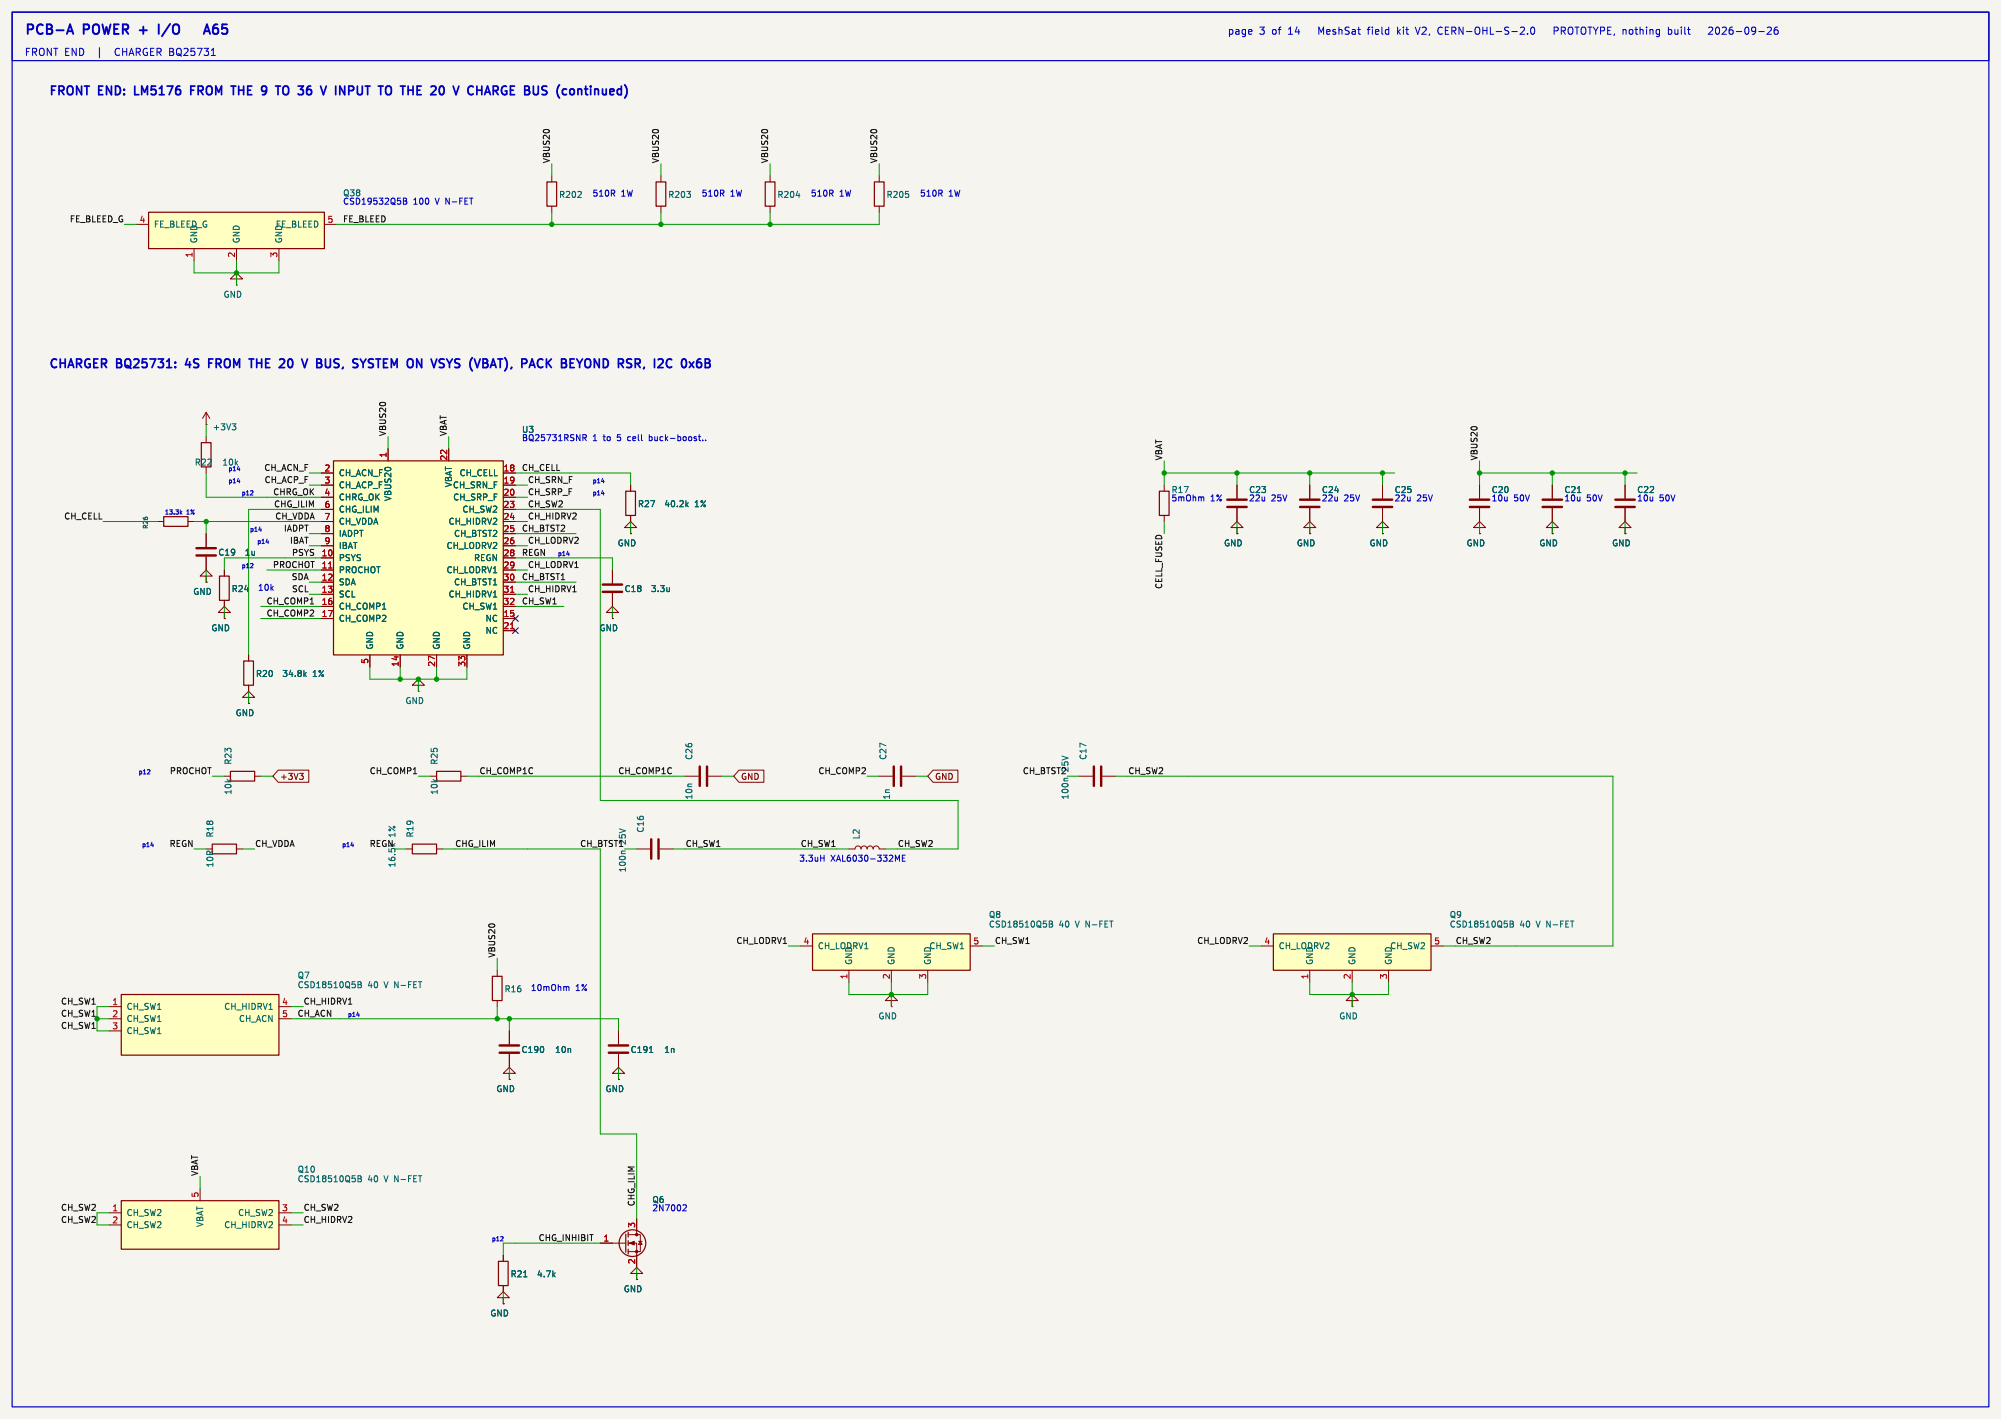
[picture p262: page 3]
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

1 GND 14 GND 27 VBAT 22 GND 33 CH_CELL

10 U8

# GND C⁷³ 100n 25V HF_CS

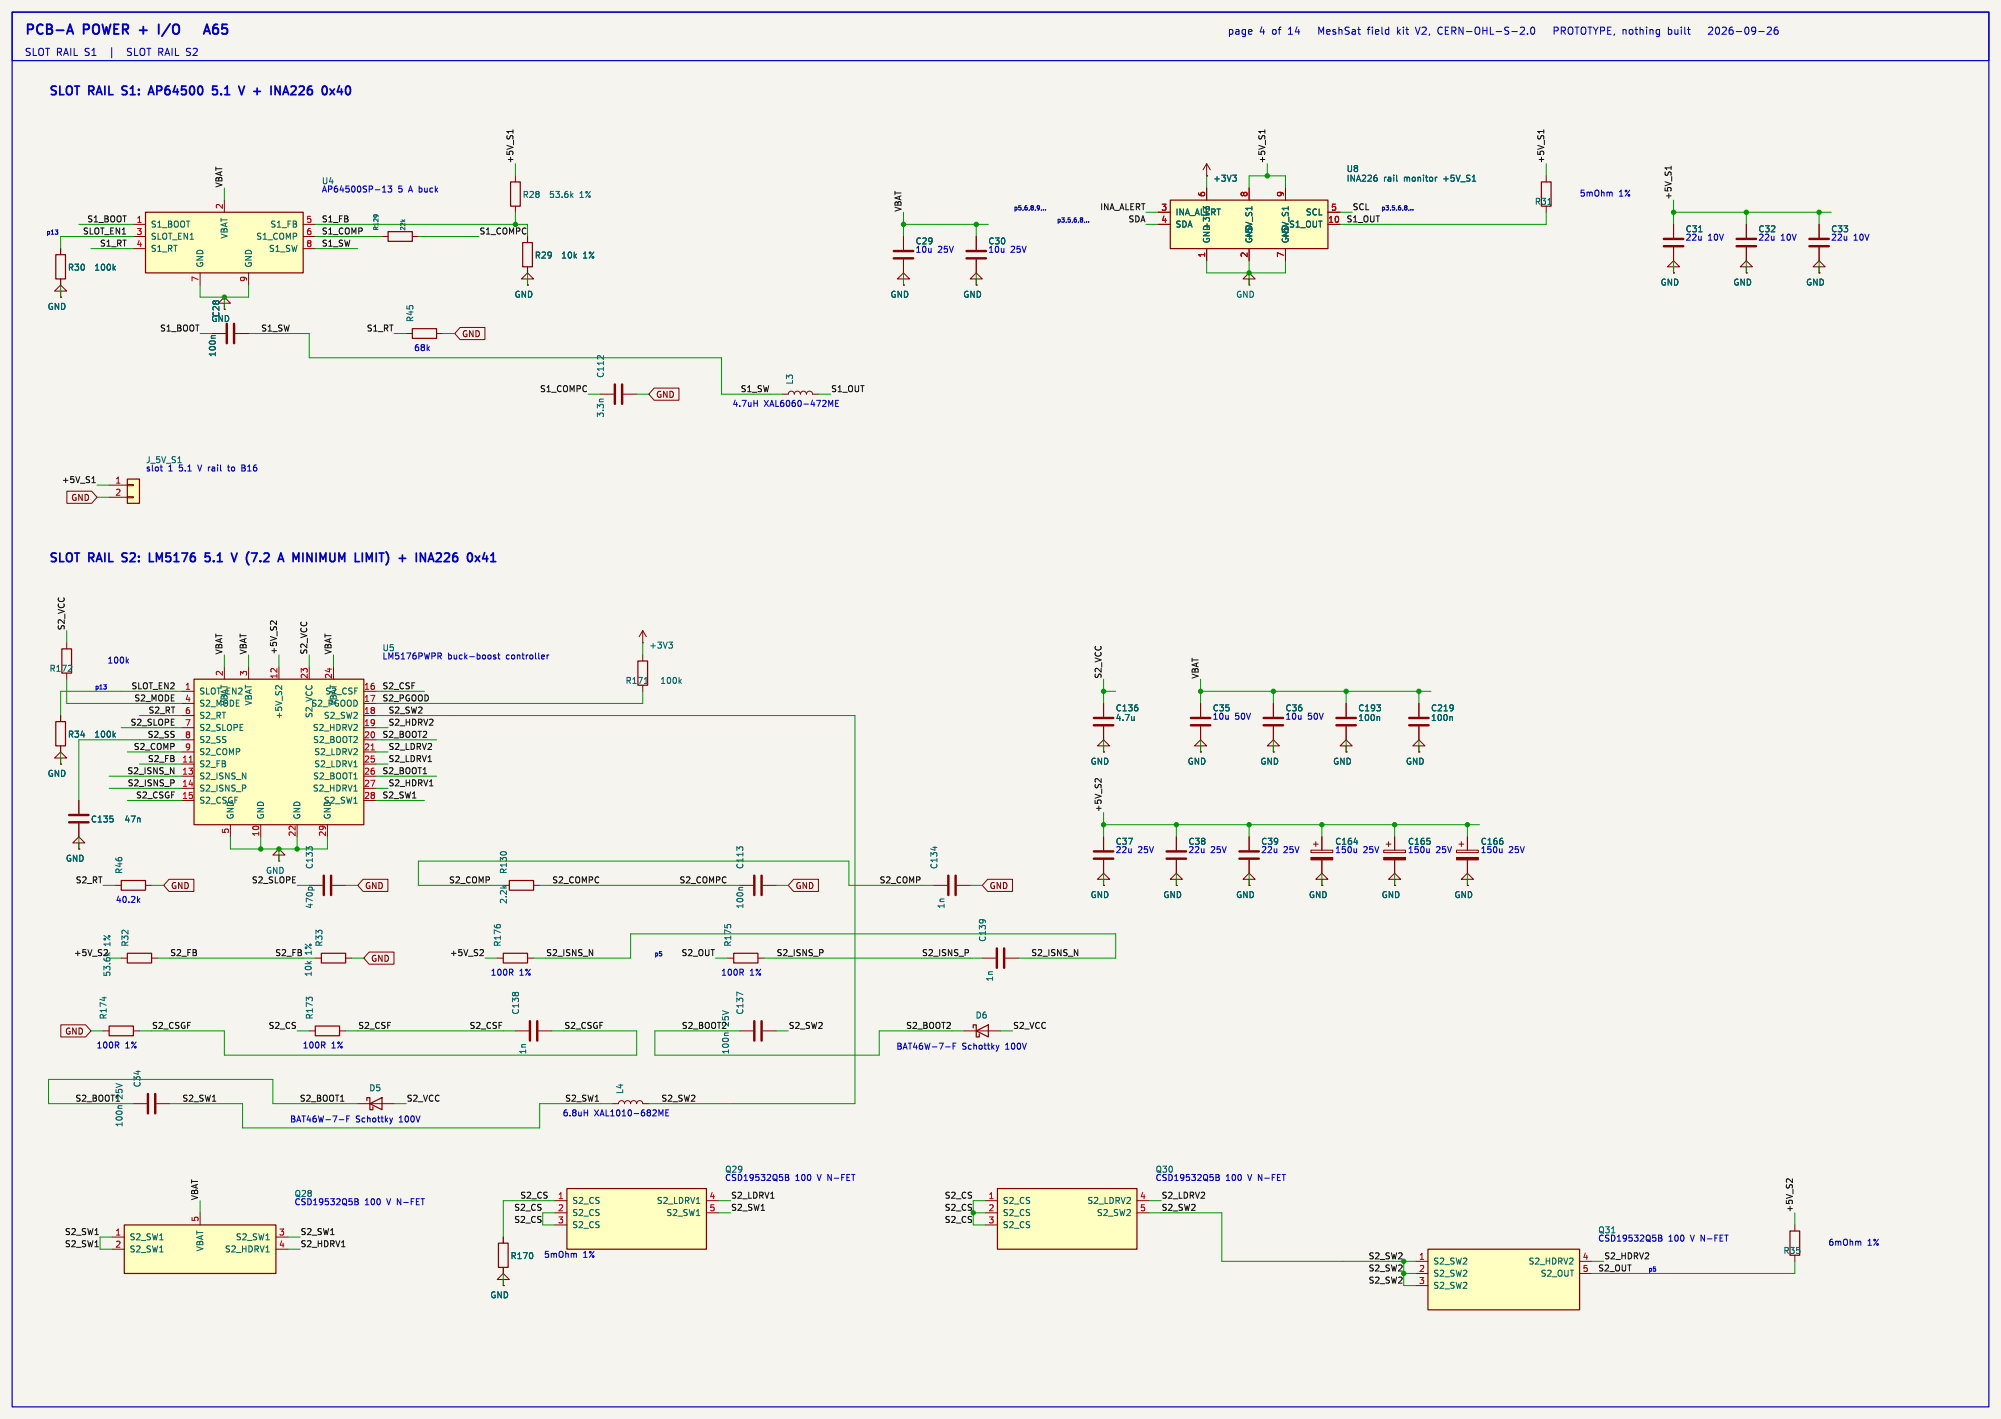
[picture p263: page 4]

p5 SLOT RAIL S2: LM5176 5.1 V (7.2 A MINIMUM LIMIT) + INA226 0x41

3 GND 10 +5V_S2 12 GND 22 S2_VCC 23 GND 29 VBAT 24 S2_CSF

POE_SW2 1 POE_SW2 2 POE_SW2 3 | POE_HDRV2 4 POE_OUT 5 Q20 | C¹²⁹ 1n | GND
R5 1k | R¹⁶⁸

C162 C³ 10u 25V ¹²¹⁰

5 Q5 | R⁹² 143k 1% R¹ 10R ²W ²⁵¹² R¹⁰ 15k | R¹⁹² 10k 1%

GND R⁷⁴ 62k 1%

100n +3V3 C² 47u 25V

GND C⁶ 680p R121 | C⁸⁷ 1.5n

GND C⁵ 220n

J_BM10 | C¹³³ 470p C⁷⁶ 470p

# 5 POE_SW1 3 POE_HDRV1 4 Q17 C213 2.2n

C161 C¹⁴⁷ 680p

C111 GND C¹⁰ 100n 25V

R68 | R²⁰⁶ 100k
4.7u GND | R⁶ 240k 1%

GND L1

GND | C⁵⁵ 22u 10V X⁷R ¹²¹⁰ | C⁵⁶ 22u 10V X⁷R ¹²¹⁰ | D3 SMBJ5.0A | GND R⁶⁷ 10k 1%
GND | R⁵¹ 10k 1%
C204 | D²⁰ C⁷⁵ 100n
D12 | C⁶¹ 100n 25V | R⁵² | C¹⁴⁸ 470p C⁵⁸ 1.5n C⁸⁰ 100n 25V
R91 | 10k GND | R²⁶ C²¹⁴ 100n
C182 | R203 R¹⁹⁹ | 47k | R⁷⁶ 105k 1%
S3_BOOT 1 SLOT_EN3 3 S3_RT 4 | GND
7 VBAT

2 GND

9 S3_FB 5 S3_COMP 6 S3_SW 8 U6

GND

R38 100k

R8 | C¹¹⁹ 10u 50V X⁷R ¹²¹⁰
J_RF9 | R⁶² R¹⁸³ GND
GND | GND R⁴⁷

GND

GND

R118 | 100k | R⁶⁰ 140k 1%
GND R¹³¹ | 22k
GND | C²⁷ 1n
+3V3 | C48
INA_ALERT 3 SDA 4 | +3V³

2 GND
1 +3V3

6 +5V_S2

# 8 GND

7 +5V_S2

9 SCL 5 S2_OUT 10 U9
INA226 rail monitor +5V_S2

C36 R¹¹⁷ 10k

GND | C³⁴ 100n 25V | C¹³⁴ 1n
GND | C⁹¹ 100n 25V L11 6.8uH XAL1010⁻682ME | R¹²⁴ 10k 1% C¹¹⁸ 10u 50V X⁷R ¹²¹⁰ GND | C¹¹³ 100n

GND

GND | R¹⁷⁶

+3V3

INA_ALERT 3 SDA 4 | +3V³

1 GND
2 +3V3

6 +5V_S3

# 8 GND

7 +5V_S3

9 SCL 5 S3_OUT 10 U10

INA226 rail monitor | +5V_S3 | R42 100k R¹⁸⁸ 40.2k 1% | L4
R189 | R¹⁷³

9 U32_ILM 7 U32_OVLO 8 U32 C138 1n R174

5 Q29 +3V3 C42
GND | C¹³⁰ 1n
C41 | C¹⁴⁵ 1n

D6 L5

D8 | D14 C¹⁴⁶ 1n R¹³³ 62k 1% C¹¹⁴ 3.3n
GND | R¹²⁹ | 22k

R37 10k 1%

1
2
J_5V_S3 | C¹¹² 3.3n
R190 | 4.7k | R¹⁷⁵ C⁶⁹ 1n
R39 | C43

1
2
J_5V_S2 | DEV_EN

R36 53.6k 1%

R145 | 100k | C¹⁴⁴ 100n 25V
C44 | C45

GND

# J_RF10 C⁴⁰ 100n

J_CP4 | R¹⁵⁰
+3V3 | R⁴¹ 10k 1%
J_BM1 GND | C⁴⁶ 100n 25V | L9 6.8uH XAL1010⁻682ME | C¹⁴⁹ 470p | C71

4 MAIN_PDT 7 KILL 8 NC 3 U1 F1 R64 3.3k D21 GND

R3 10k R184 | 39k 1% | C⁷² 100n 25V
C31 R2100k | R⁶¹ 10k 1%
J_CN2 | R¹⁸¹

GND

+3V3 GND

GND

GND

POE_SW2 | VBAT
POE_HDRV2 | +12V_HF | HF_SW1
POE_ISNS_P | VBAT
POE_ISNS_N | VBAT | VBAT | +5V_S² | S1_SW
HF_MODE | HF_SW2 POE_VCC
POE_EN | +12V_HF
PD_CC1 POE_CS | +5V_S¹
POE_CS VBAT | VBAT | +12V_HF
S2_LDRV1 SLOT_EN2 | S2_SW2 +54V_POE
+5V_S1 +54V_POE | POE_LDRV1 POE_SW1

SD_CSF KILL

CELL_FUSED | PD_VCC
RF_WIFI24 | CELL+ | REGN ⁺⁵V_DEV
MAIN_PB | PD_SW

SD_OUT SCL SD_SW1 VBAT

KILL | VBAT | VBAT | SD_VCC
MAIN_PDT | +12V_HF
SLOT_EN3 | VBAT
FE_BOOT2 | VBAT | U22_OVLO
FE_BOOT2 | +5V_DEV
FE_BOOT1 | FE_SW1 | VHEAT | PD_CTL1
CELL_FUSED | VBAT | PD_VCC | VBAT

S3_RT

# PD_SW1 ⁺⁵V_S³ ⁺⁵V_S³

SD_SLOPE SD_VCC VBUS_WALL

S3_COMPC | VBAT S3_SW

S3_OUT

+5V_DEV | VBUS_WALL VBAT USBX_FLT | AB_SPARE

S3_COMPC
+5V_S3 | VBAT | +54V_POE | POE_VCC | VBAT POE_EN

S3_SW

S3_BOOT S3_RT
S3_COMP
SLOT_EN3 | S3_BOOT | S3_SW

INA_ALERT SDA

S3_FB

USBX_FLT | VBUS²⁰
SLOT_EN1 | VBUS²⁰ VIN_RAW FE_VCC VIN_RAW

# RF_5G1 VBUS²⁰

SD_SW1 FE_VCC

FE_FB | VBAT | +54V_POE
FE_MODE | VBAT
FE_COMP | +5V_DEV

INA_ALERT

HF_ISNS_N ⁺⁵V_S² | SCL | SD_BOOT2 SD_OUT | SD_ISNS_P
+5V_S2

# +13V8_PA ⁺⁵V_S³ S2_OUT

SDA

S3_OUT SCL

U32_OVLO | +5V_S³ RF_WIFI24 | RF_5G1
POE_SW2 POE_COMP | PA_VCC | VBAT
POE_FB | POE_FB | +13V⁸_PA

CH_LODRV2 EXP²_SPD

p4 | 100k
LM5176PWPR buck-boost | controller p3,4,6,8,..

slot 2 5.1 V rail to B16

AP64500SP-13 5 A buck

slot 3 5.1 V rail to B16

p3,4,6,8,..

p3,4,6,8,..

p4,6,8,9,..

10u 25V

40.2k 10u 25V

22u 10V

p13 | BAT46W-7-F | Schottky 100V
22u 10V

## SLOT RAIL S3: AP64500 5.1 V + INA226 0x44

SLOT RAIL S2 | | SLOT RAIL S3 PCB-A POWER + I/O | A65

68k

## SLOT RAIL S2: LM5176 5.1 V (7.2 A MINIMUM LIMIT) + INA226 0x41 (continued)

4.7uH XAL6060-472ME

22u 10V

p2 | page 5 of 14 | MeshSat field kit V2, CERN-OHL-S-2.0 | PROTOTYPE, nothing built | 2026-09-26

5mOhm 1%

# D22 R¹⁵⁵

# R5 1k R¹⁶⁸

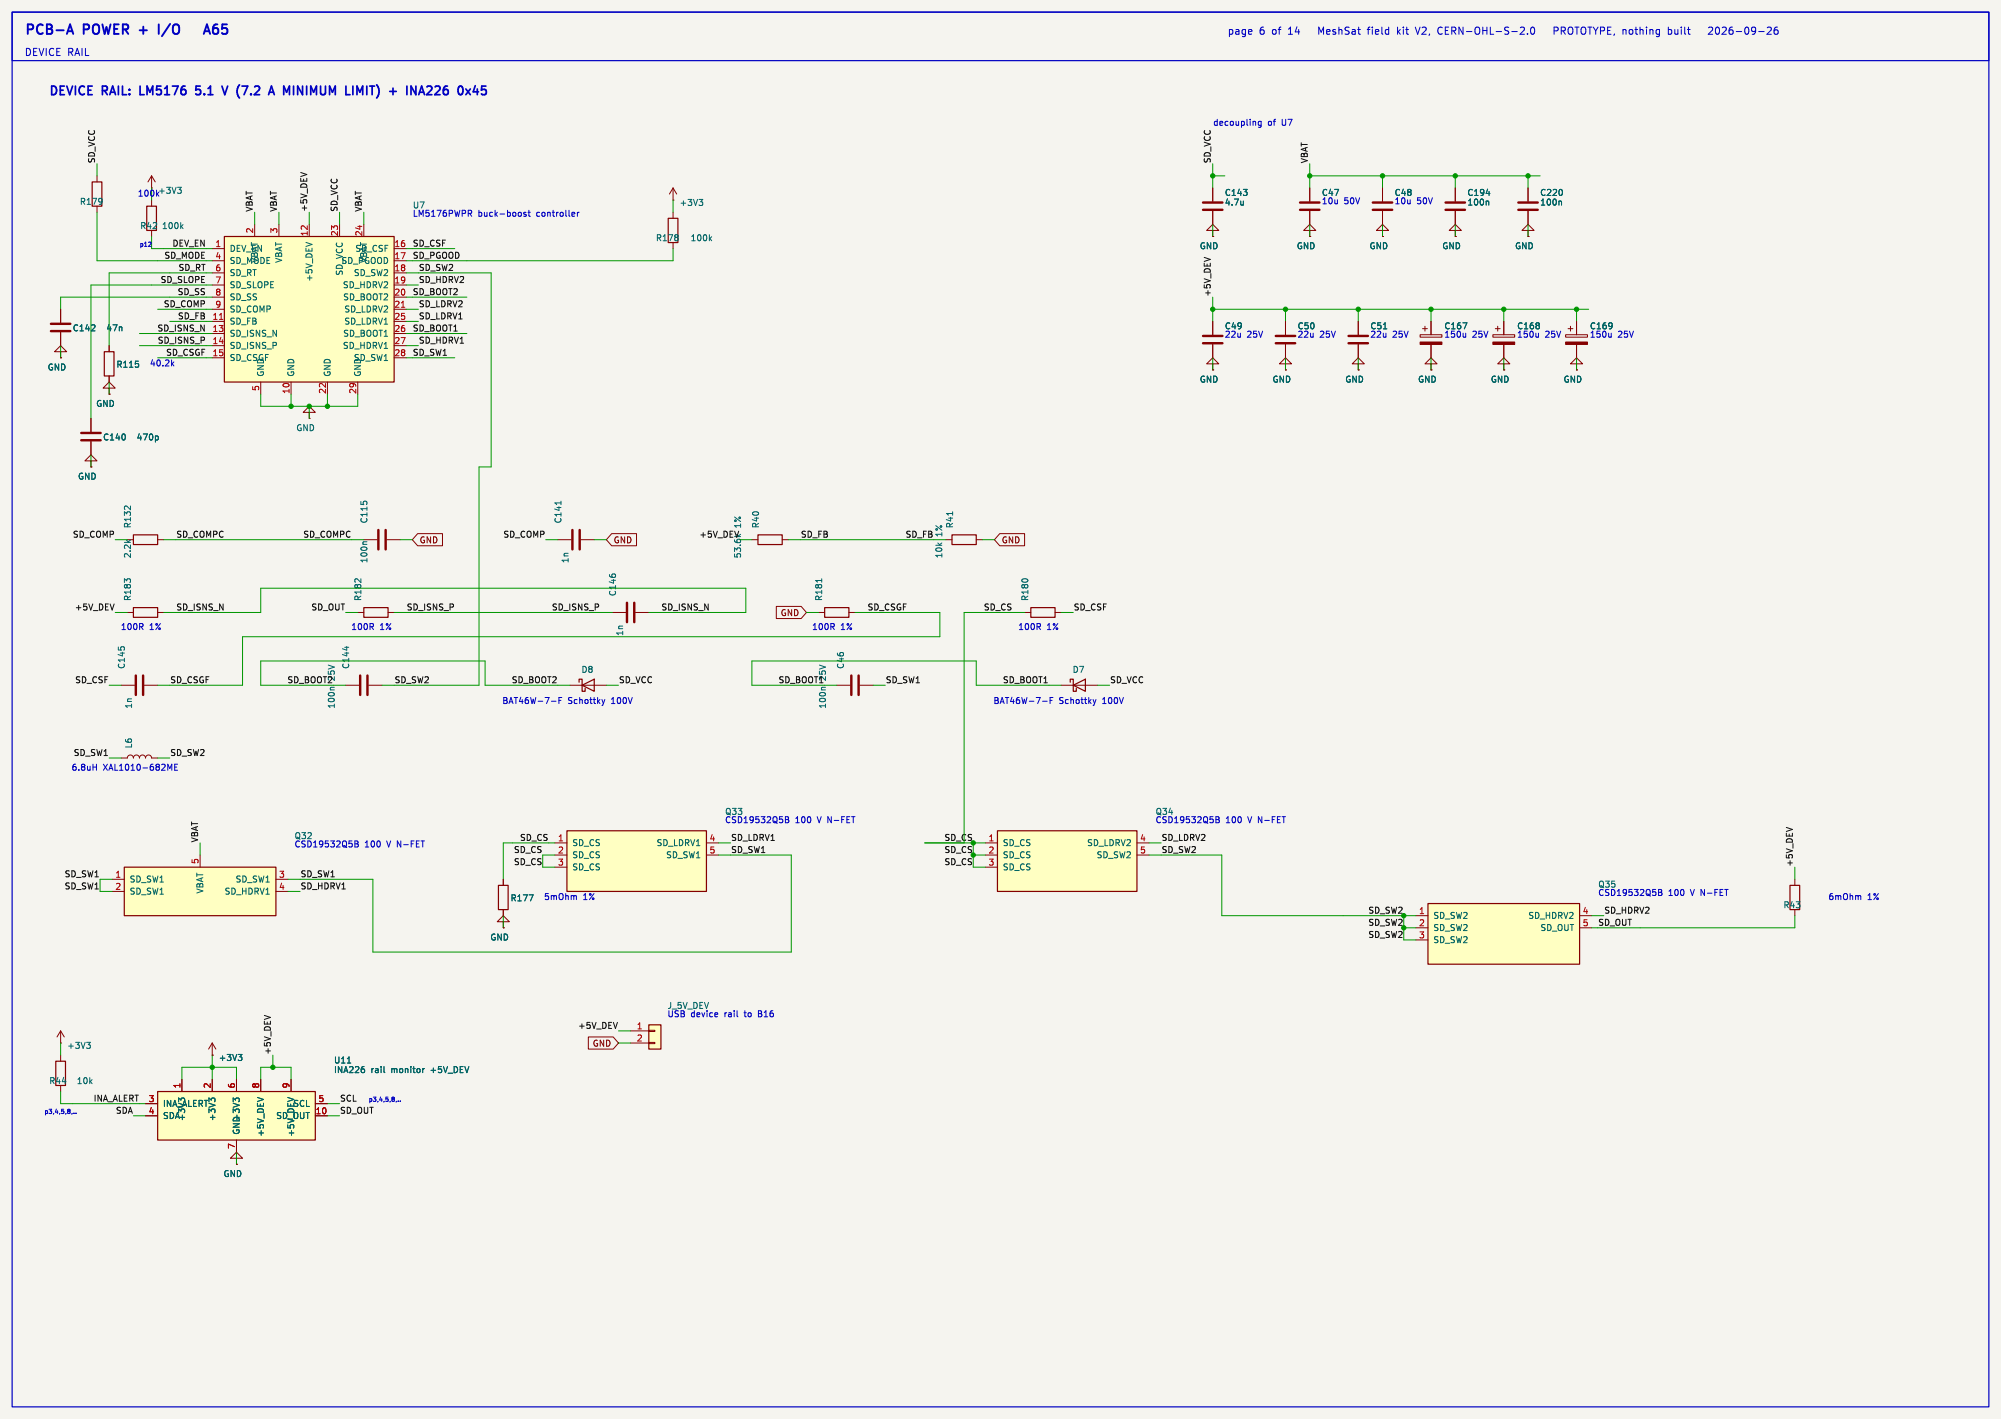
[picture p264: page 6]

USB device rail to B16

C13 C¹²⁸ 1n | L12
5 Q7 CSD18510Q5B | 40 V N-FET D² | +3V3

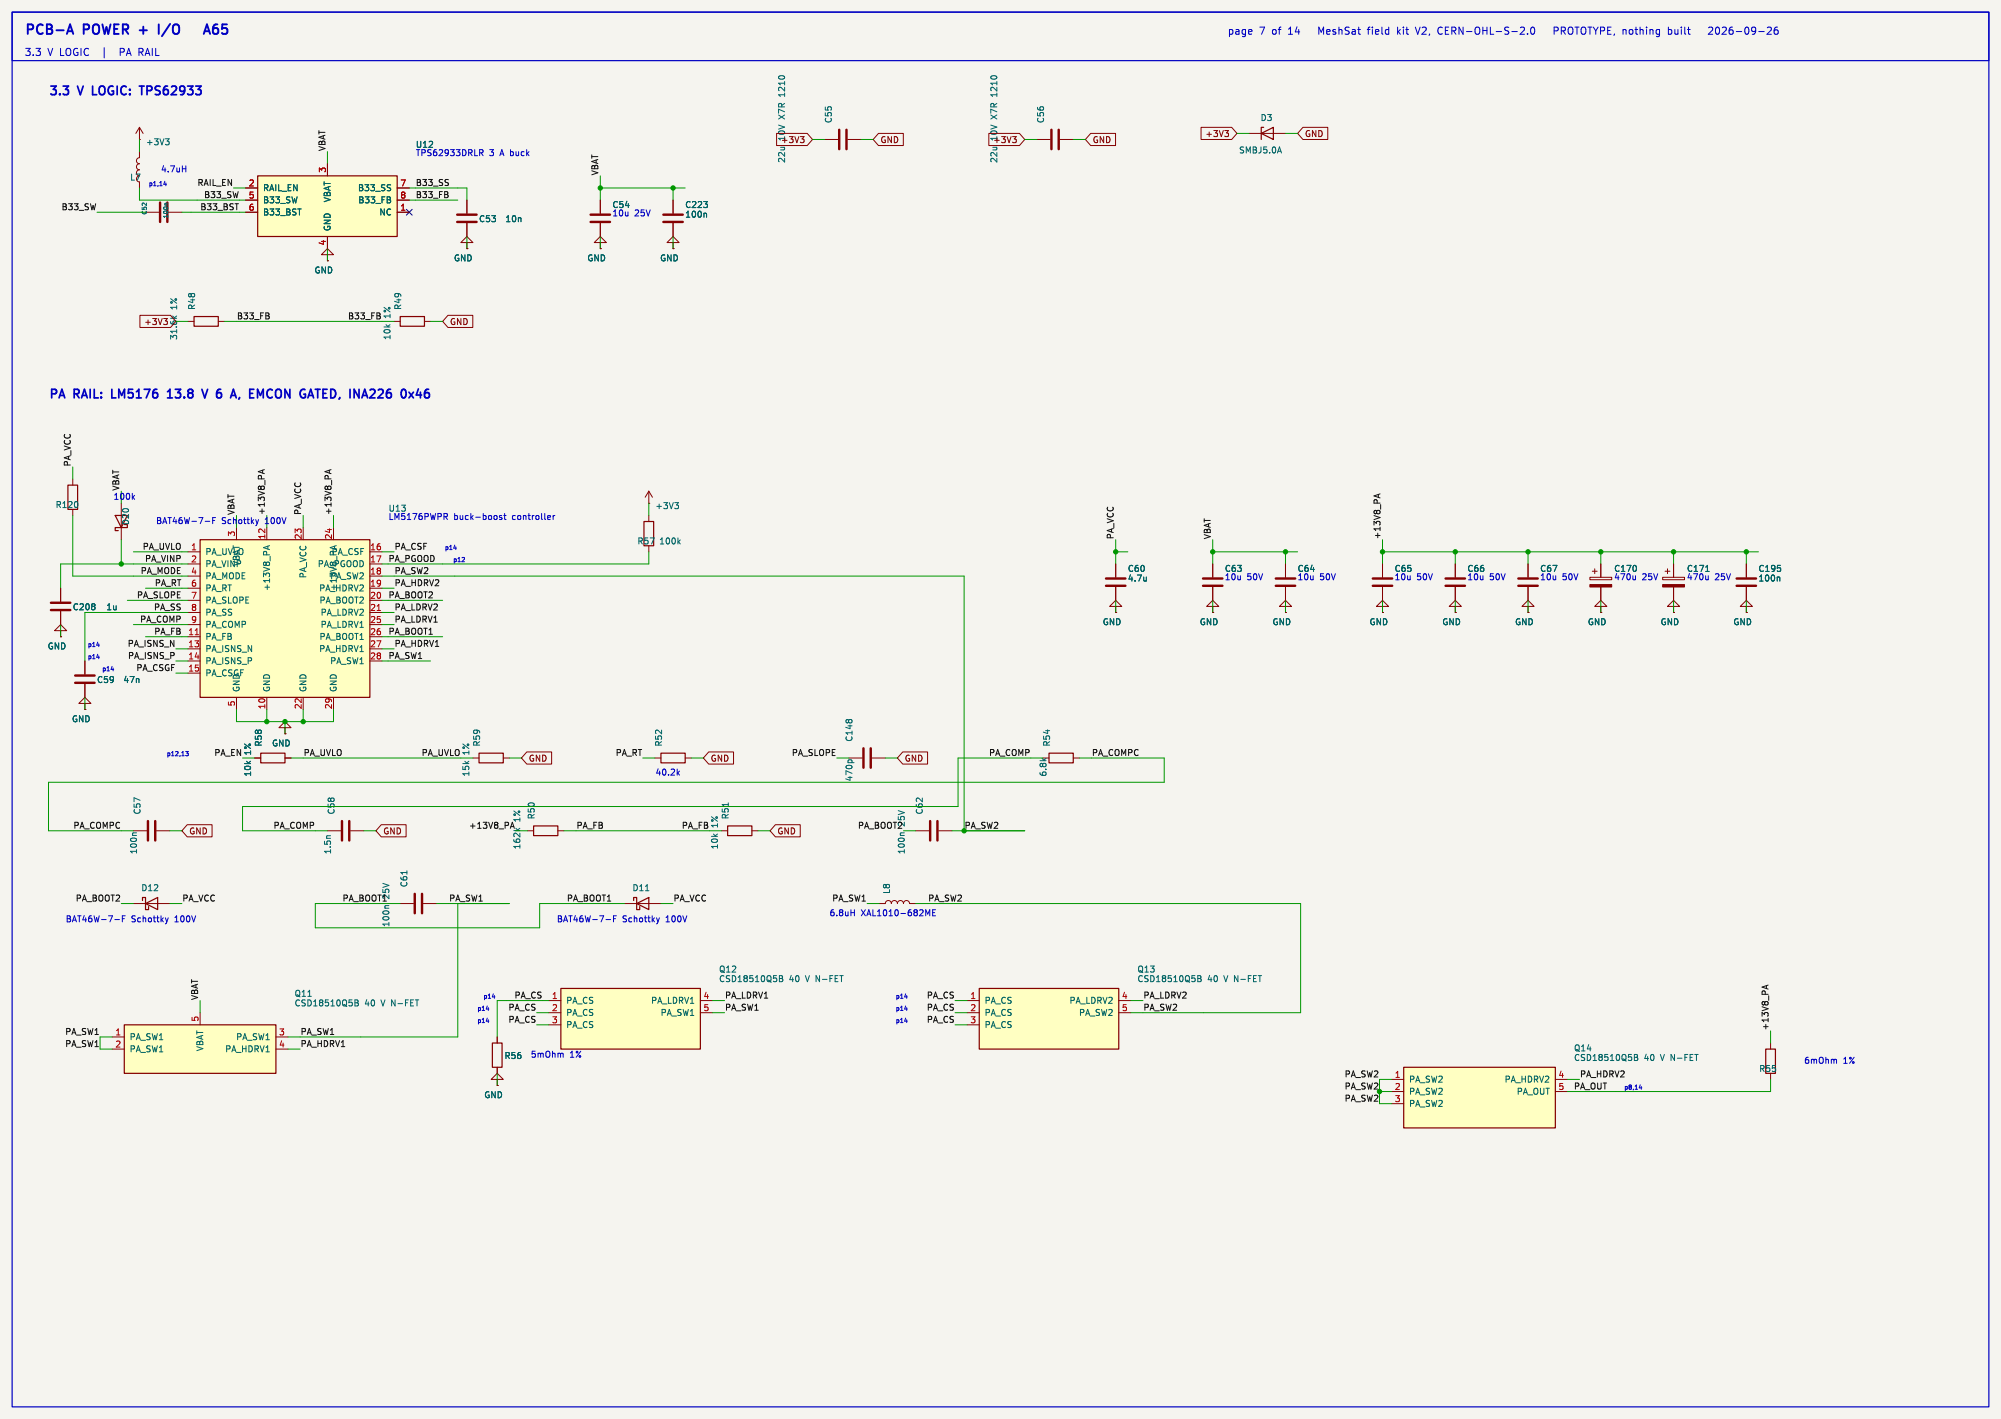
[picture p265: page 7]

GND C⁷³ 100n 25V | HF_CS
POE_PGOOD | +5V_S²

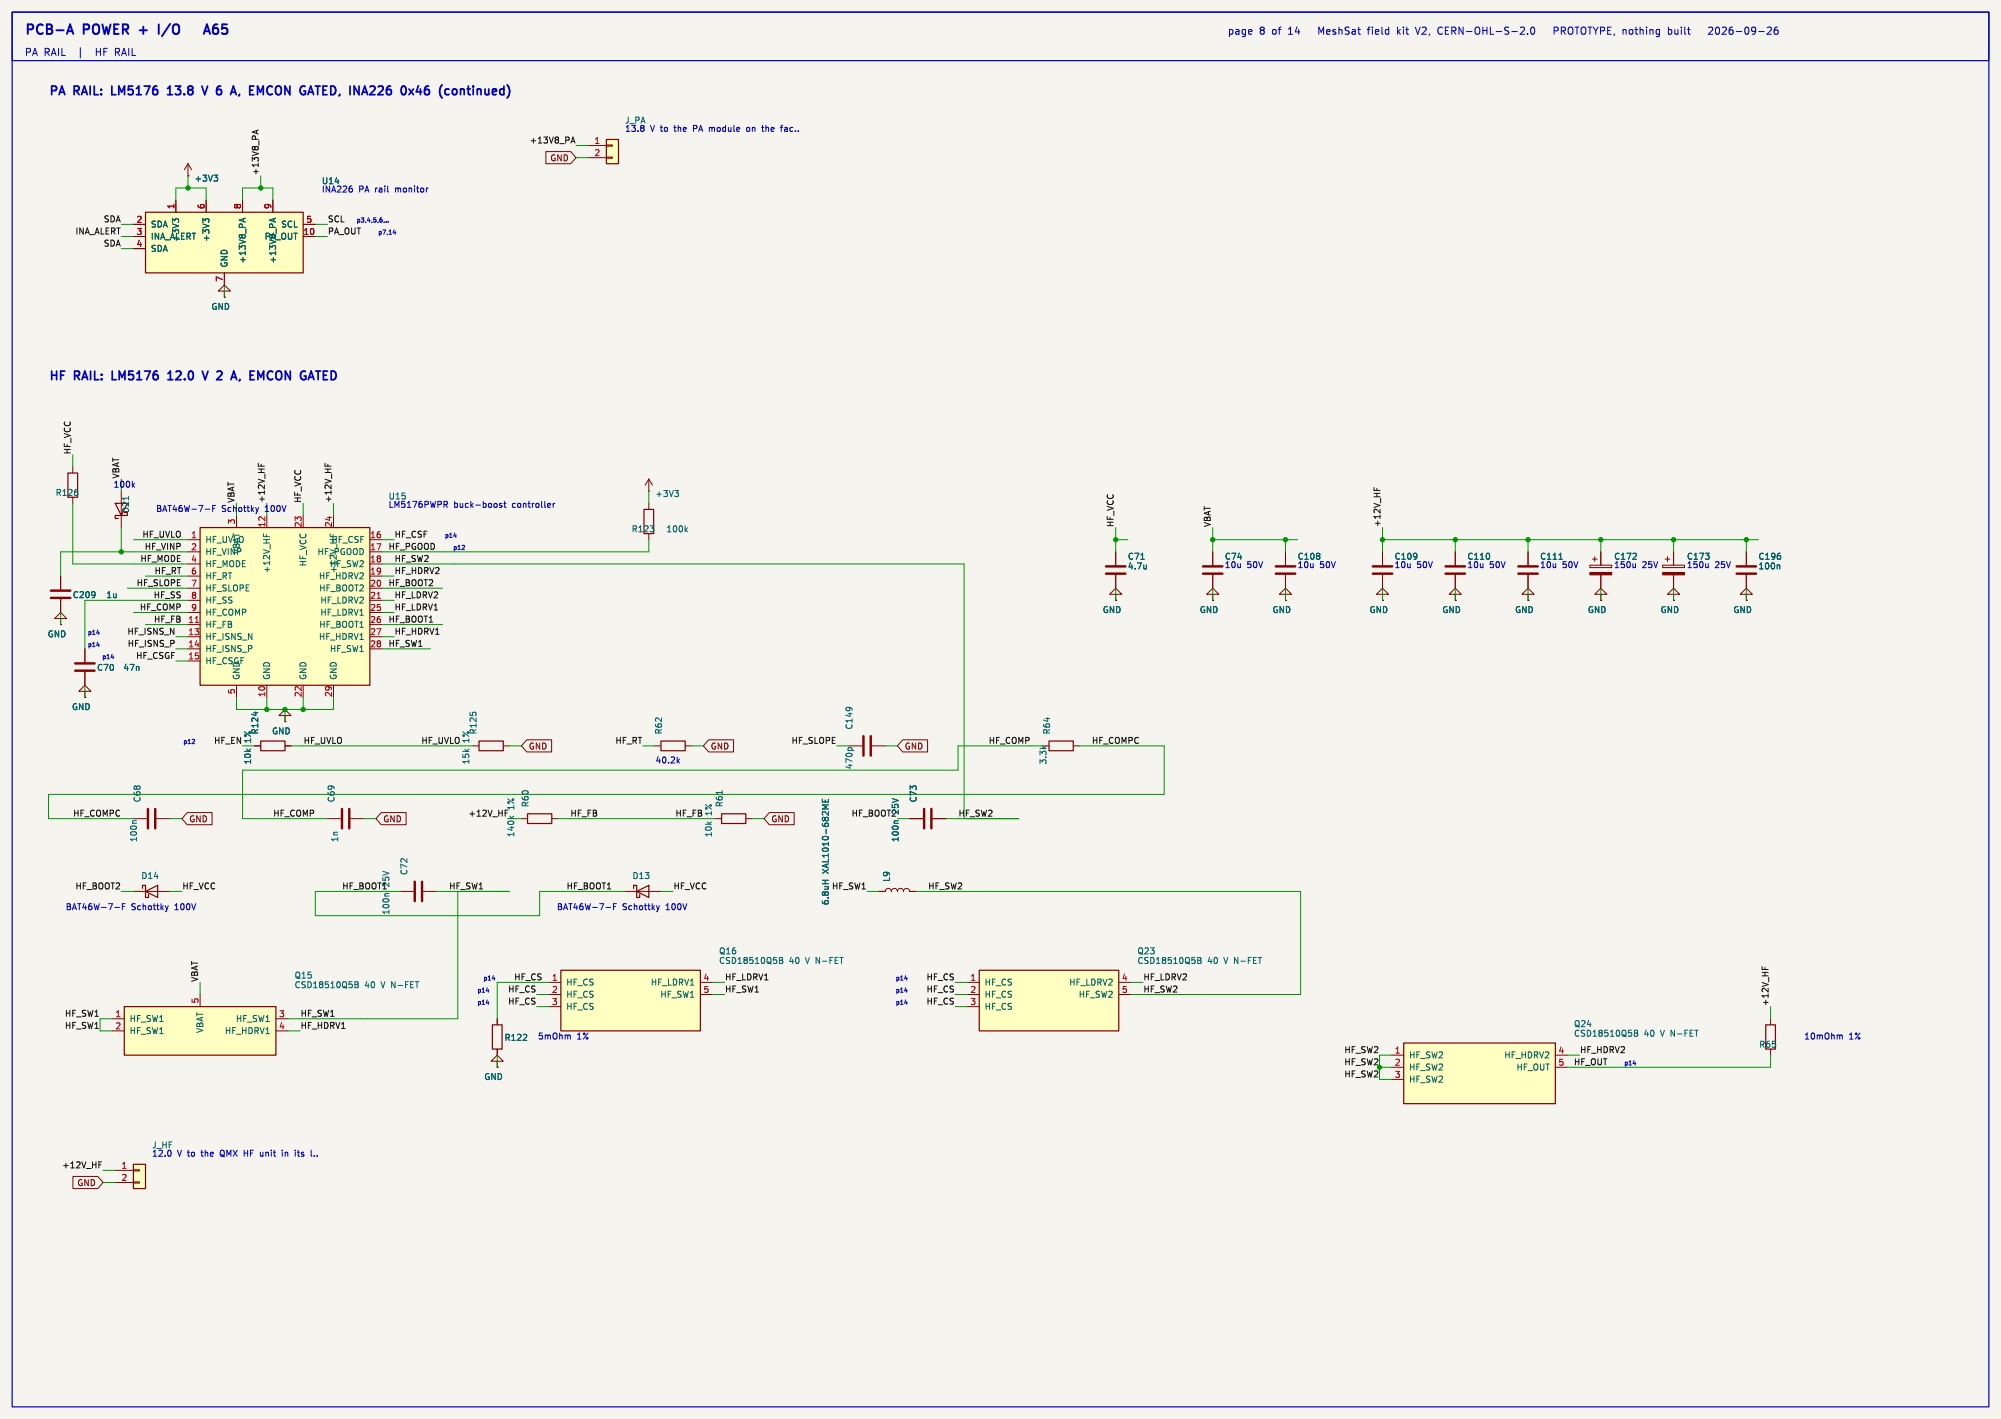
[picture p266: page 8]

13.8 V to the PA module on the fac..

R5 1k | R¹⁶⁸
R68 | R²⁰⁶ 100k

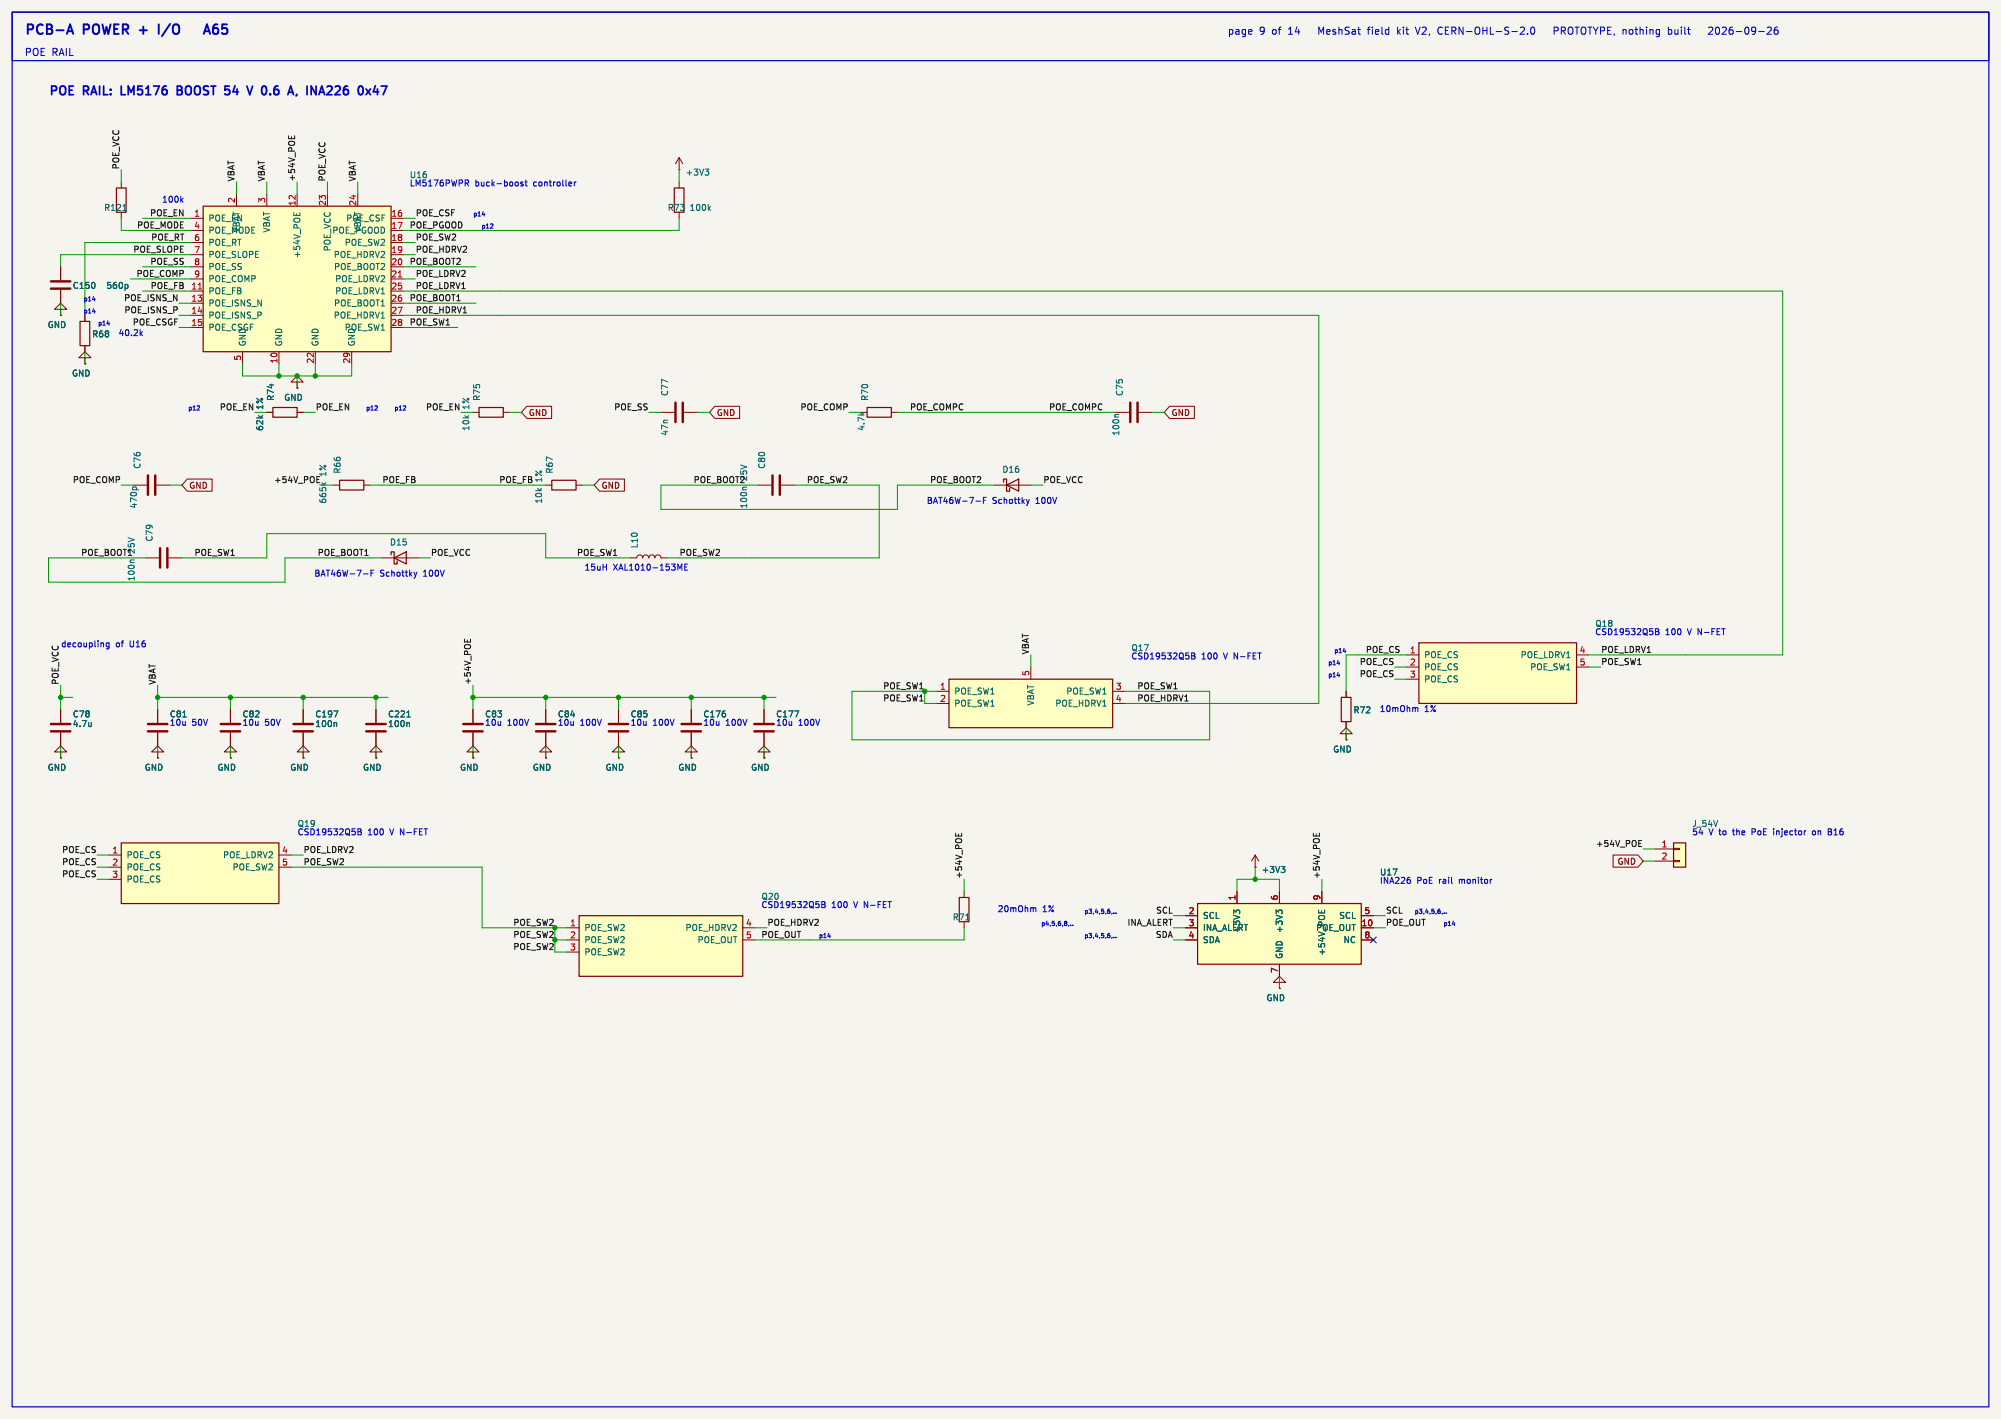
[picture p267: page 9]

3 GND 10 +54V_POE 12 GND 22 POE_VCC 23 GND 29 VBAT 24 POE_CSF 16 POE_PGOOD 17 POE_SW2 18 POE_HDRV2 19 POE_BOOT2 20 POE_LDRV2 21 POE_LDRV1 25 POE_BOOT1 26 POE_HDRV1 27 POE_SW1 28 U16

# D22 R¹⁵⁵

# R5 1k R¹⁶⁸

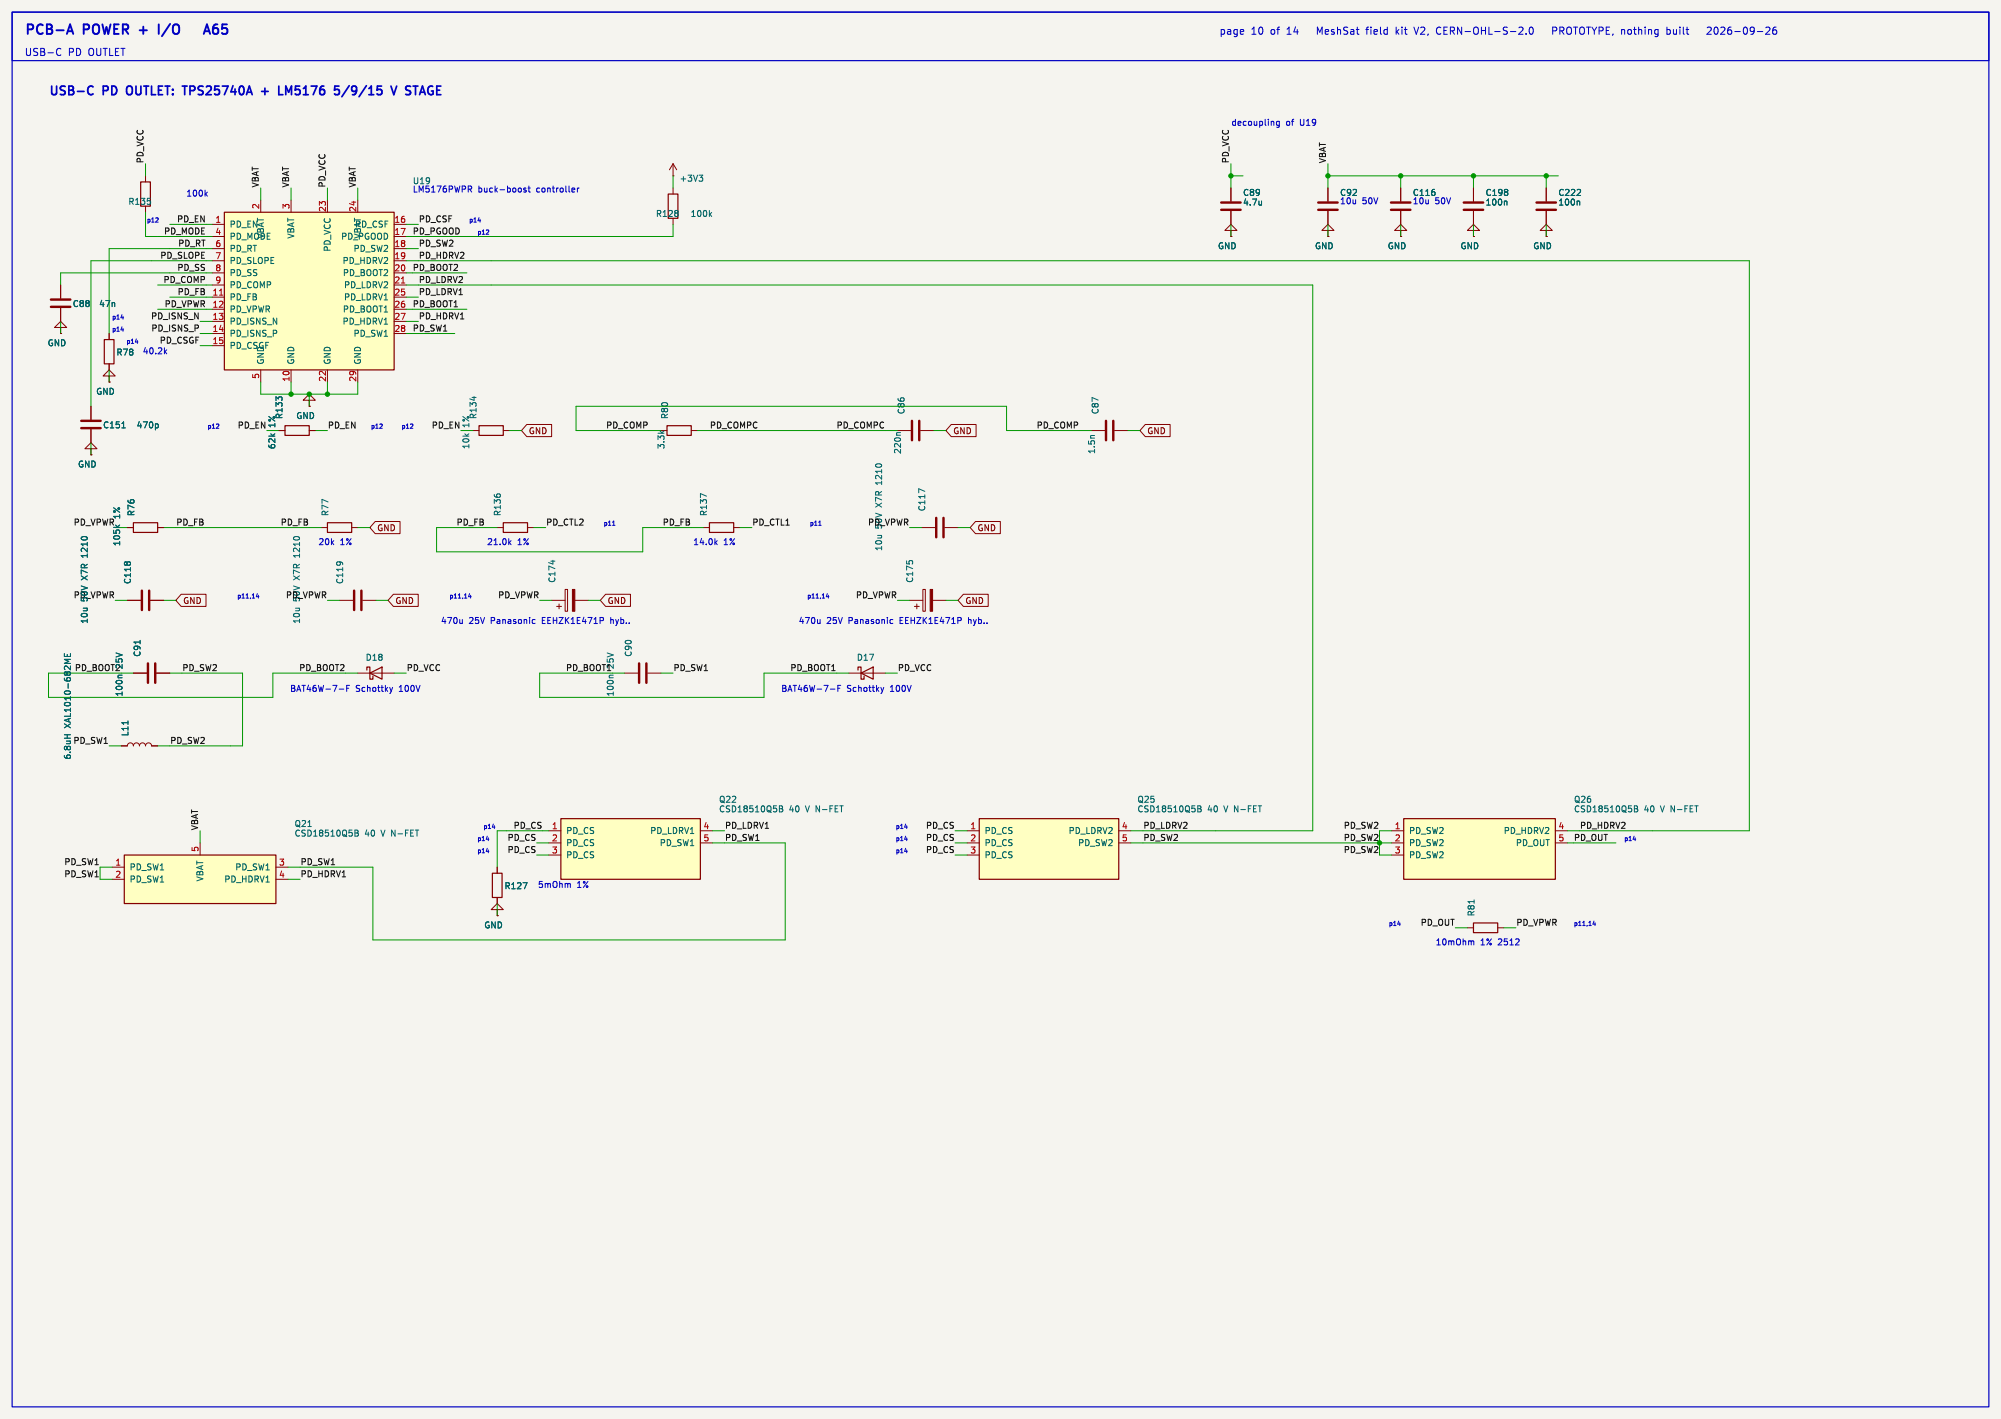
[picture p268: page 10]

3 GND 10 PD_VCC 23 GND 22 VBAT 24 GND 29 PD_CSF

24 U18

# C13 C¹²⁸ 1n L12

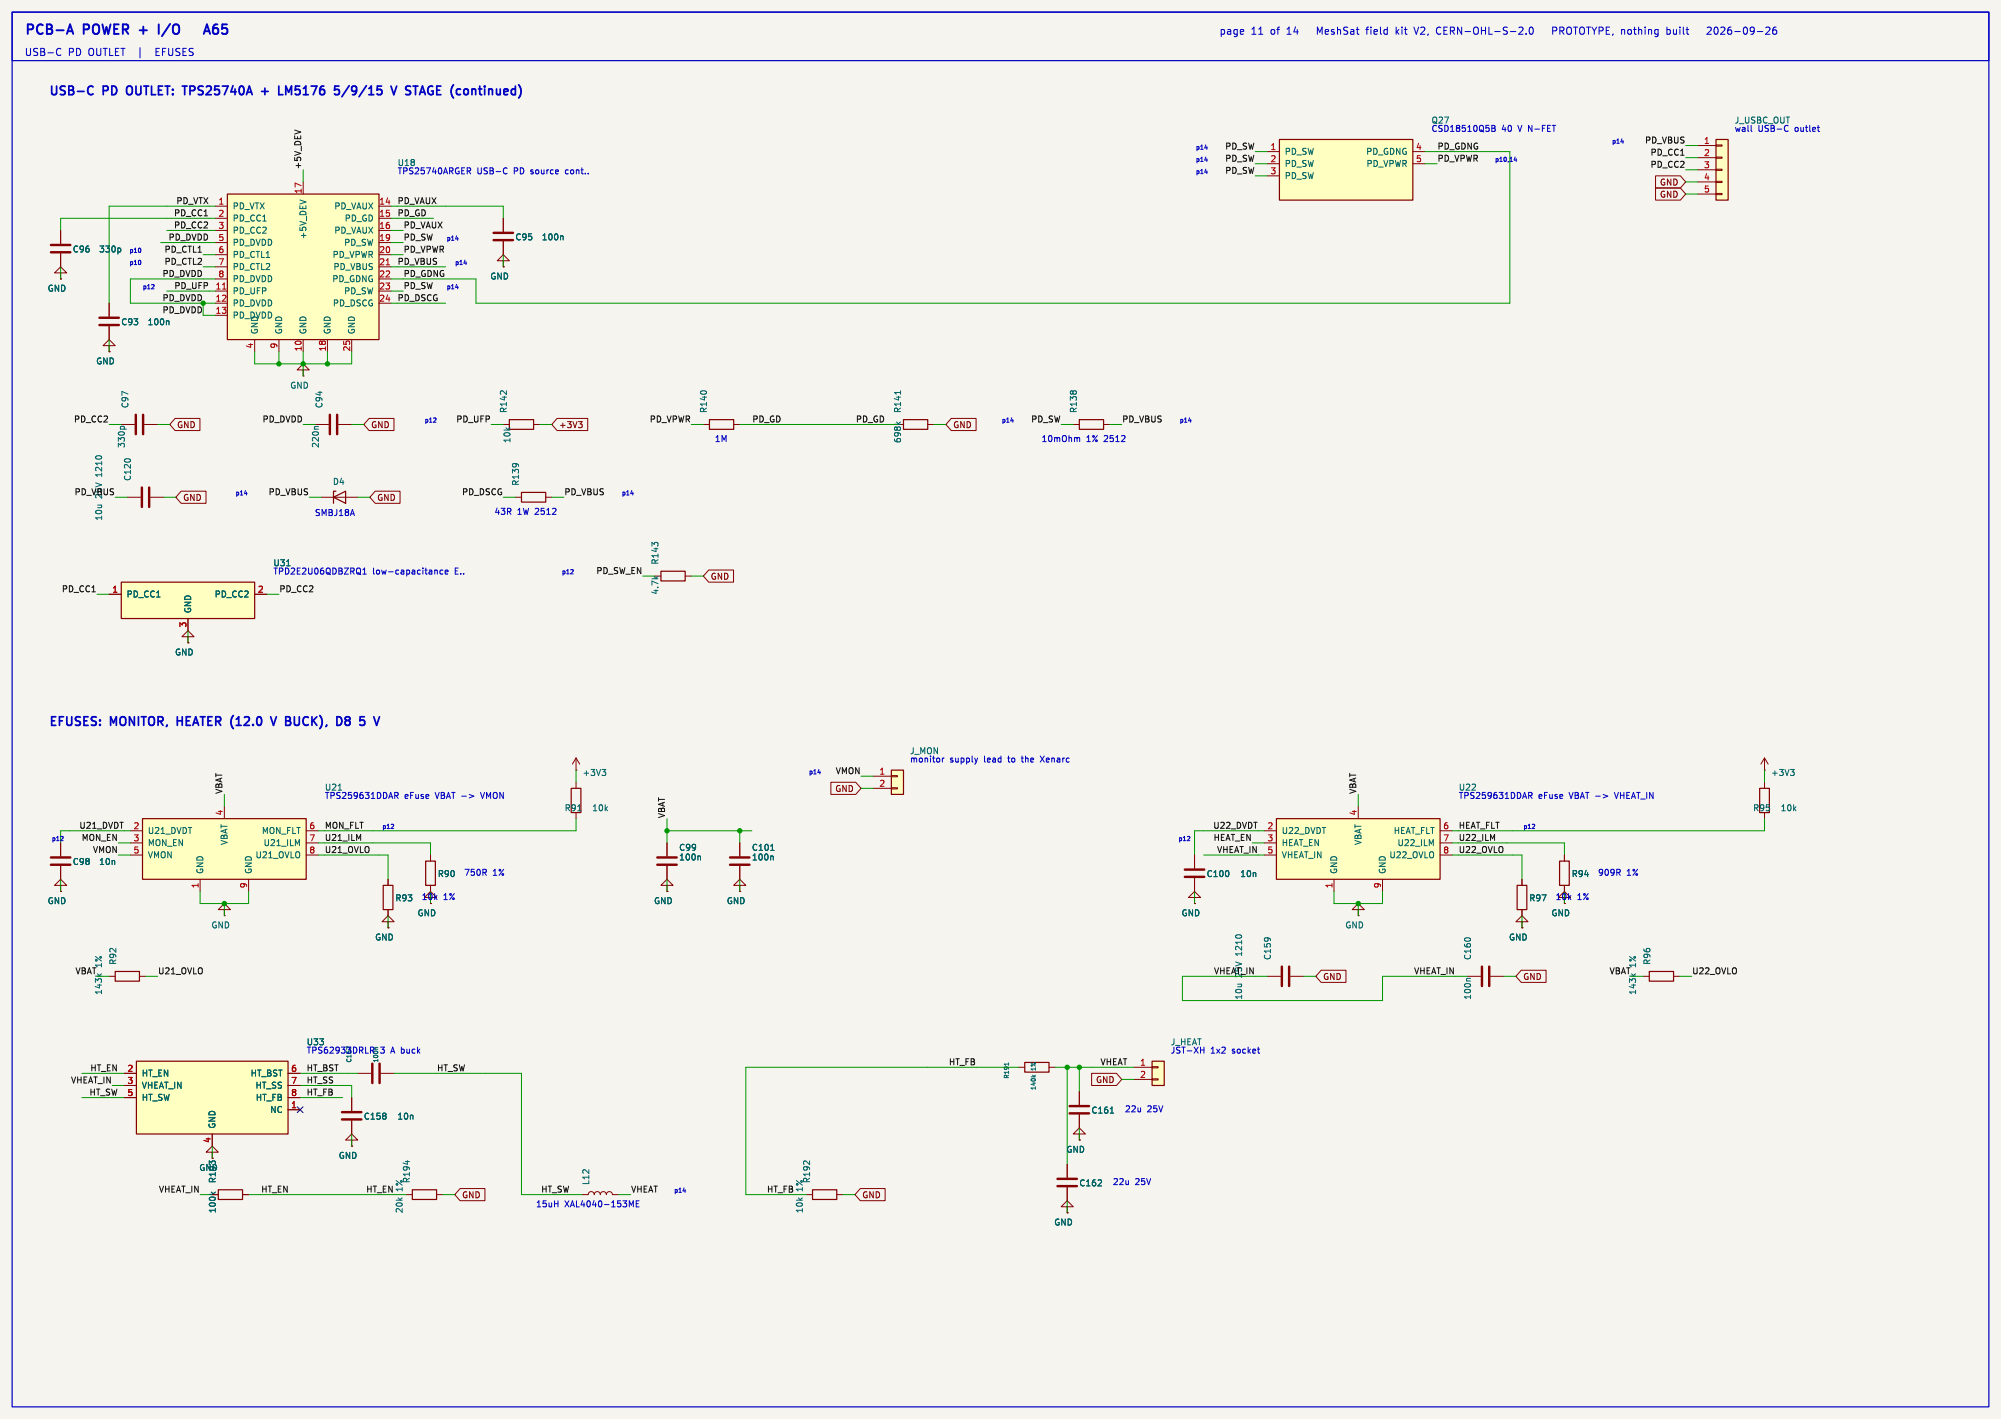
[picture p269: page 11]

GND | GND
POE_PGOOD | +5V_S²

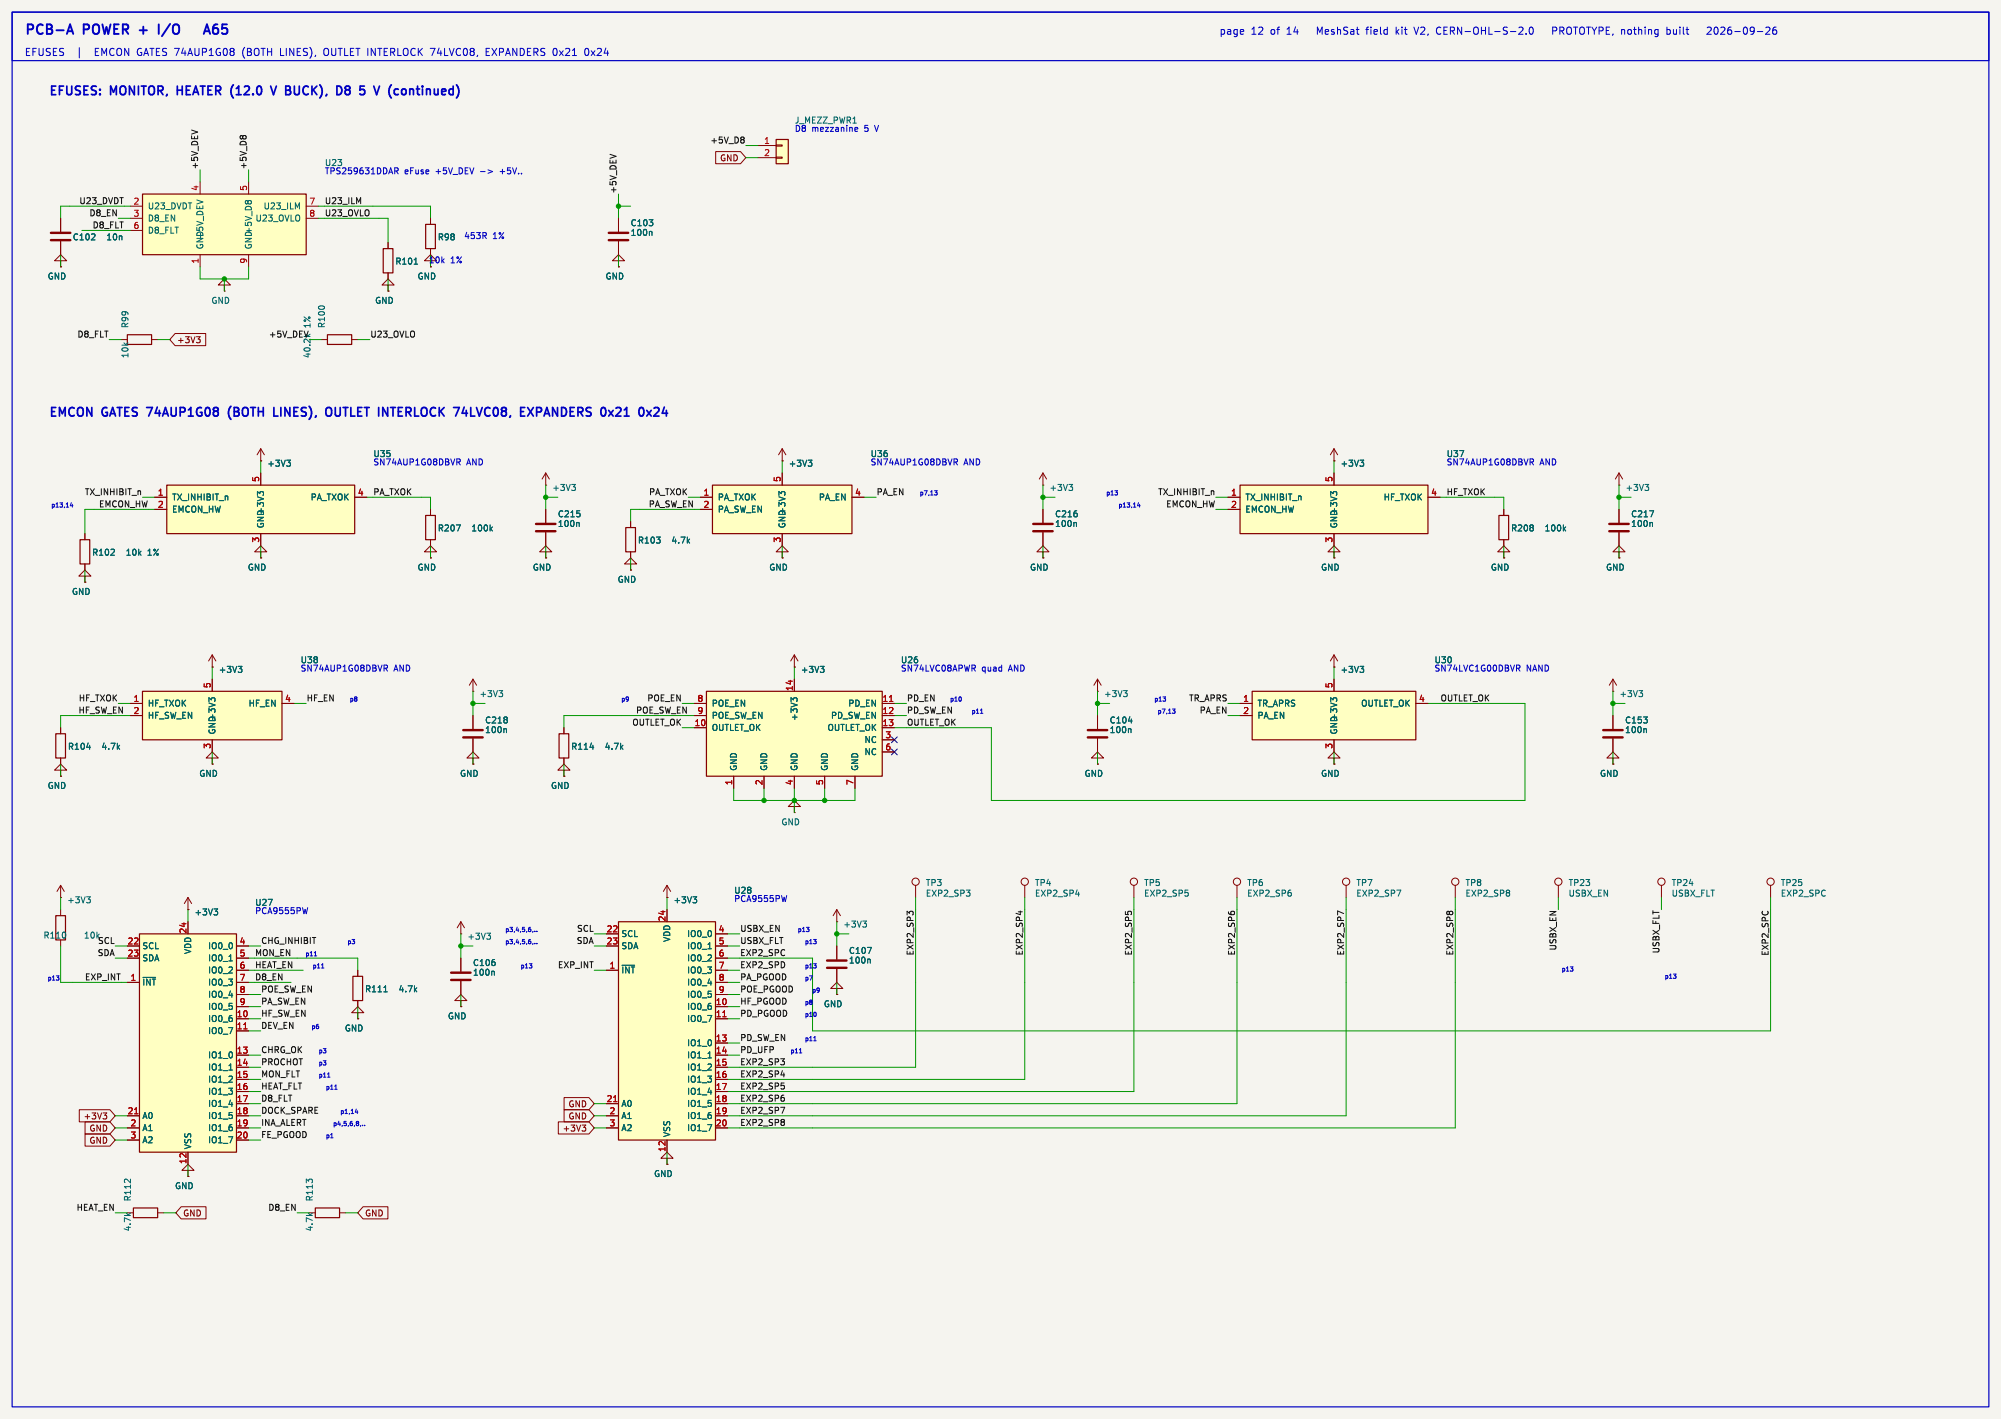
[picture p270: page 12]

R5 1k | R¹⁶⁸
GND | C¹³⁰ 1n

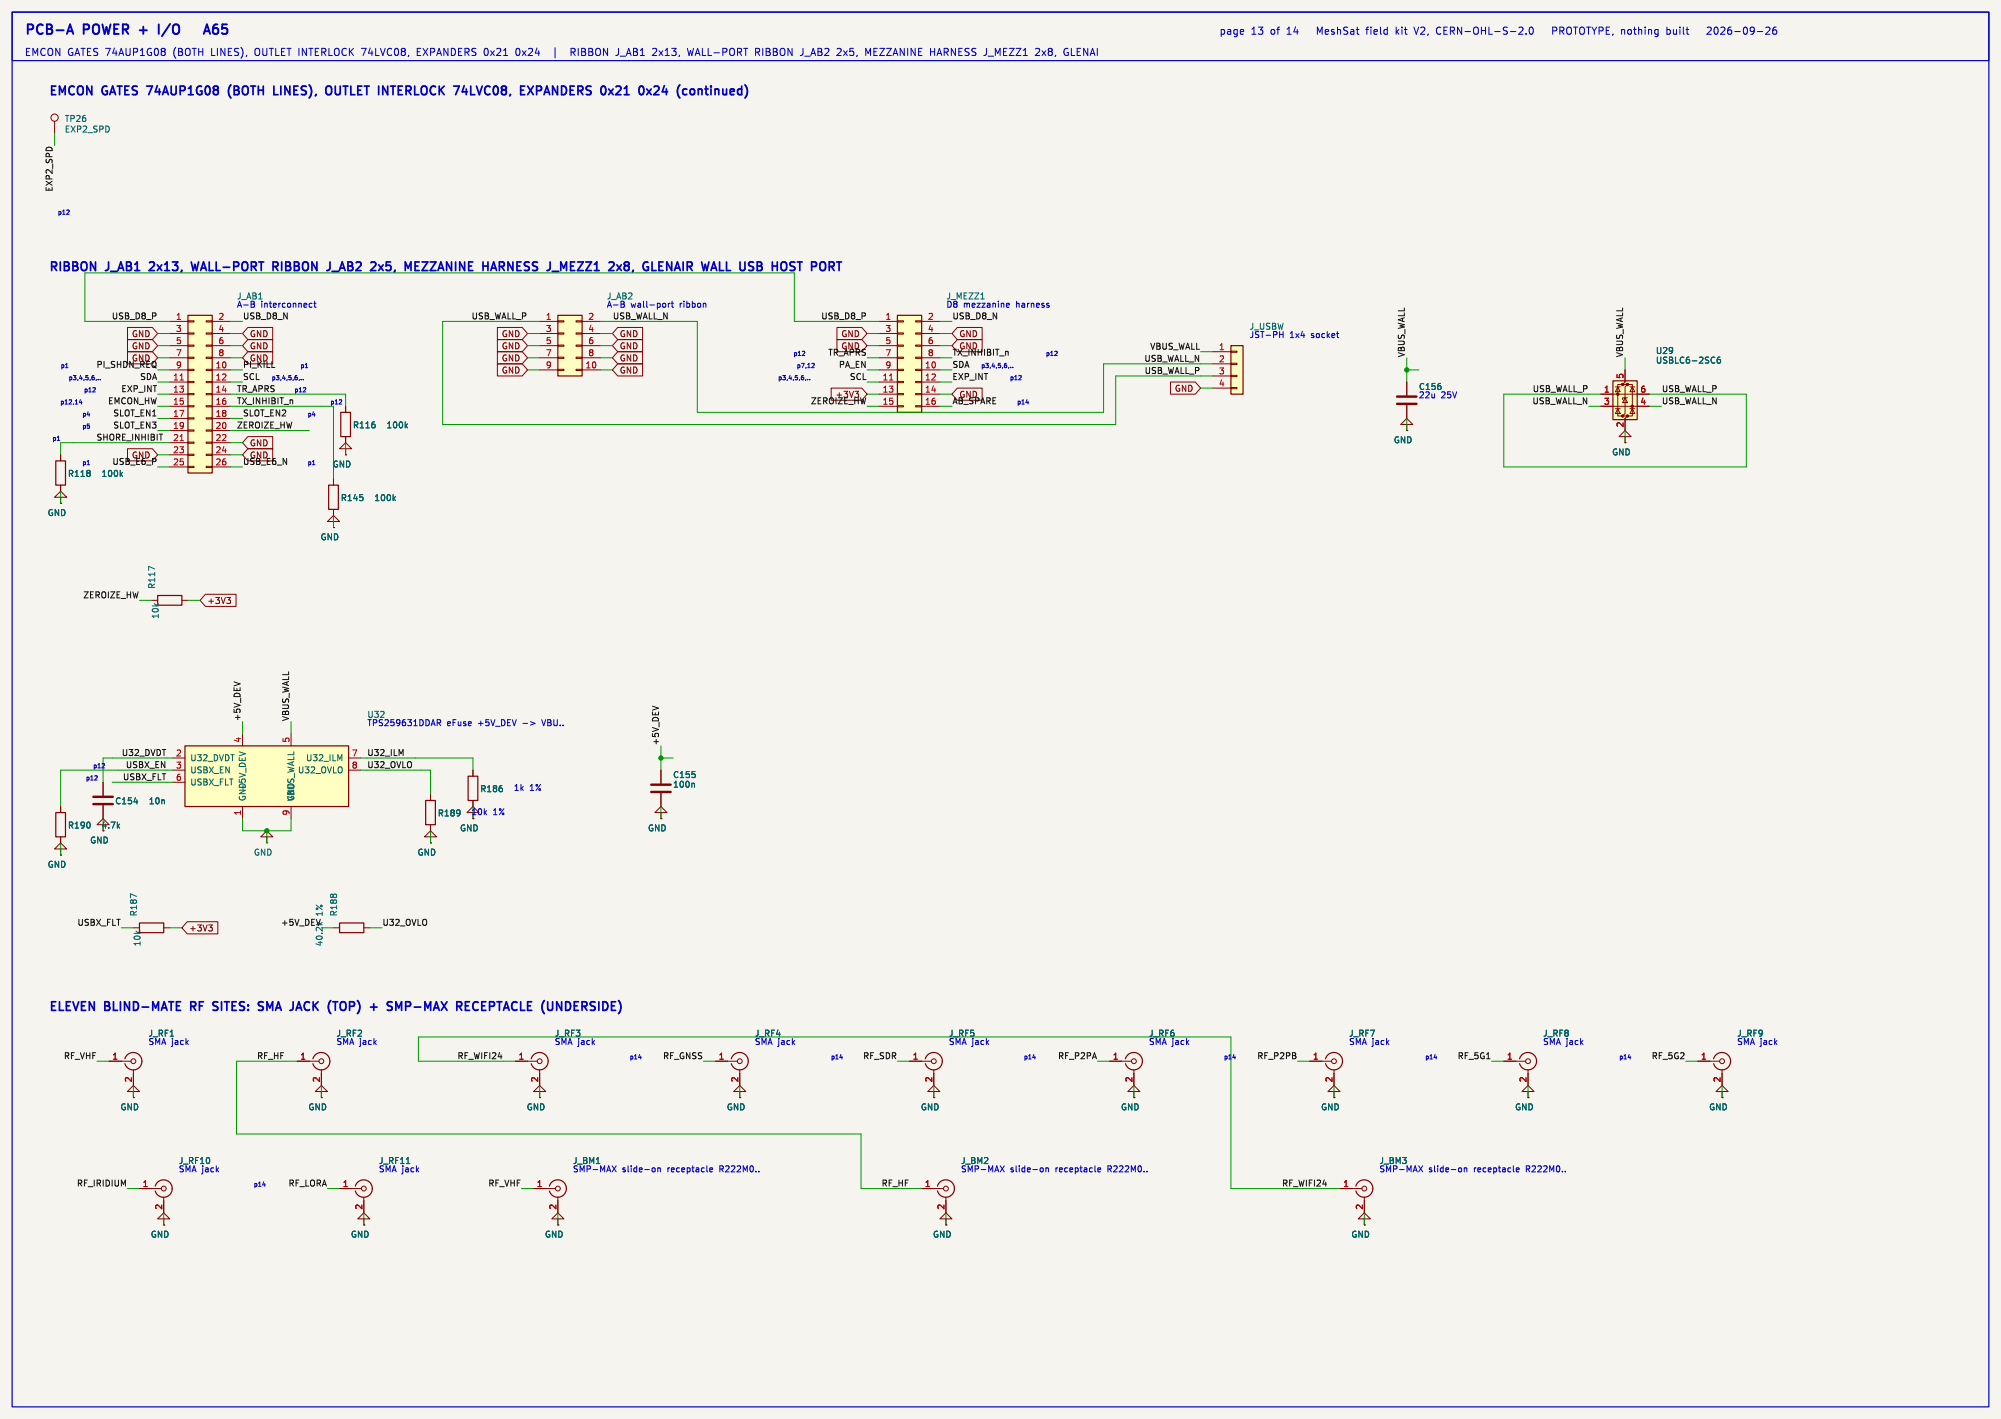
[picture p271: page 13]

p13 RIBBON J_AB1 2x13, WALL-PORT RIBBON J_AB2 2x5, MEZZANINE HARNESS J_MEZZ1 2x8, GLENAIR WALL USB HOST PORT

# D22 R¹⁵⁵

# R5 1k R¹⁶⁸

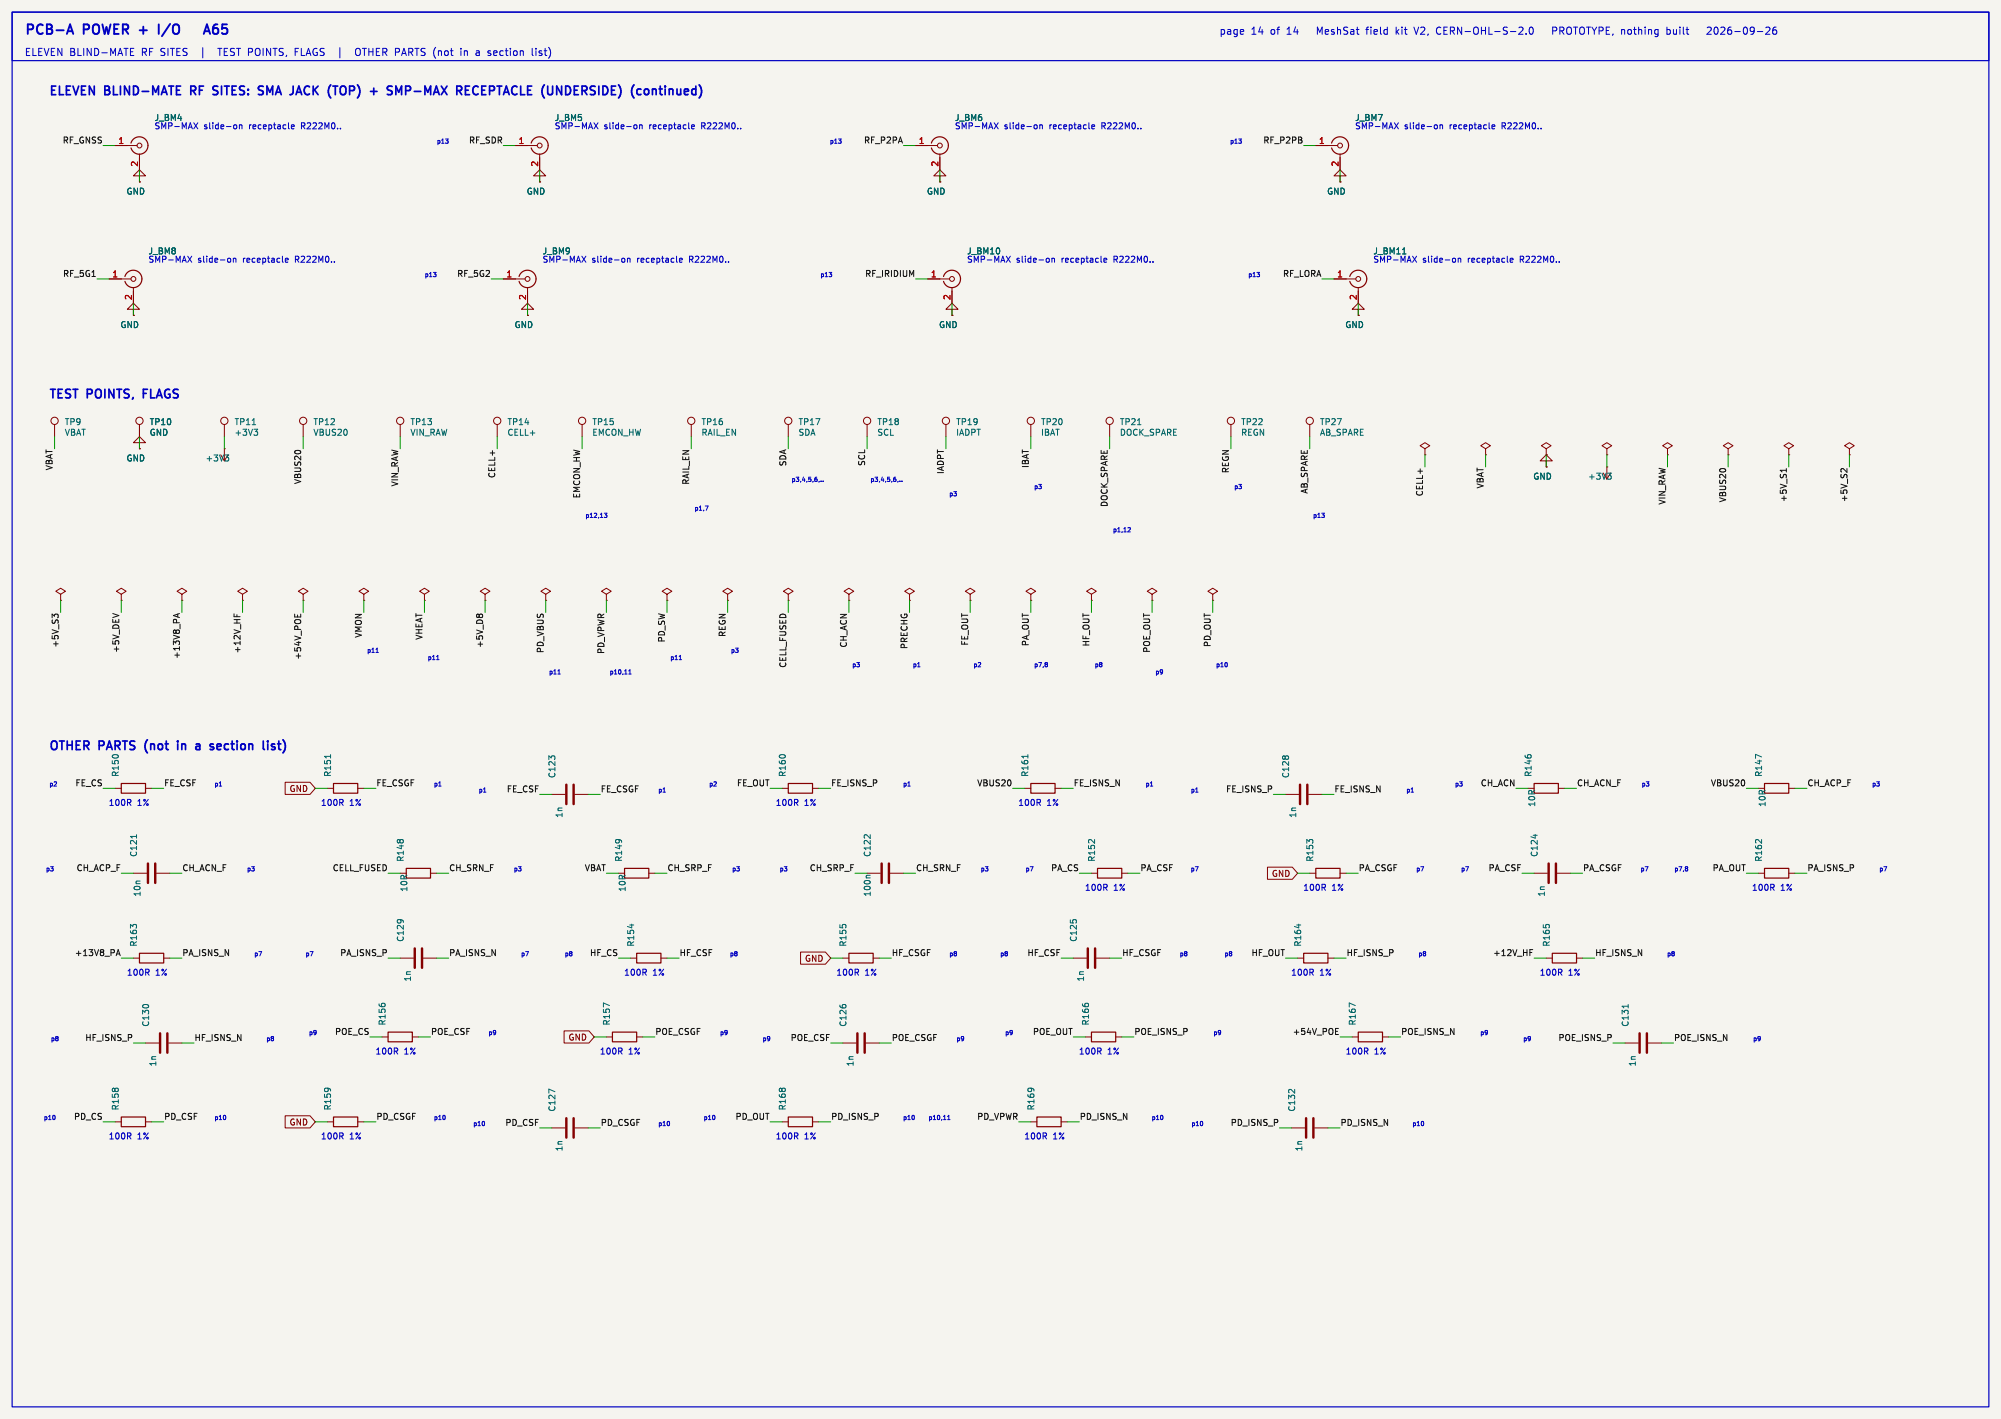
[picture p272: page 14]

ELEVEN BLIND-MATE RF SITES: SMA JACK (TOP) + SMP-MAX RECEPTACLE (UNDERSIDE) (continued)

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

OTHER PARTS (not in a section list)
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
