meshsat/meshsat-fieldkit/v2/release/handover/H1/v2/release/handover/_generated/pcb-c-display-c8/pcb-c-display-schematic.pdf

10u | R³¹ 300R
SCL | SDA ⁺³V³ Q4_G | +3V³ | SCL SDA

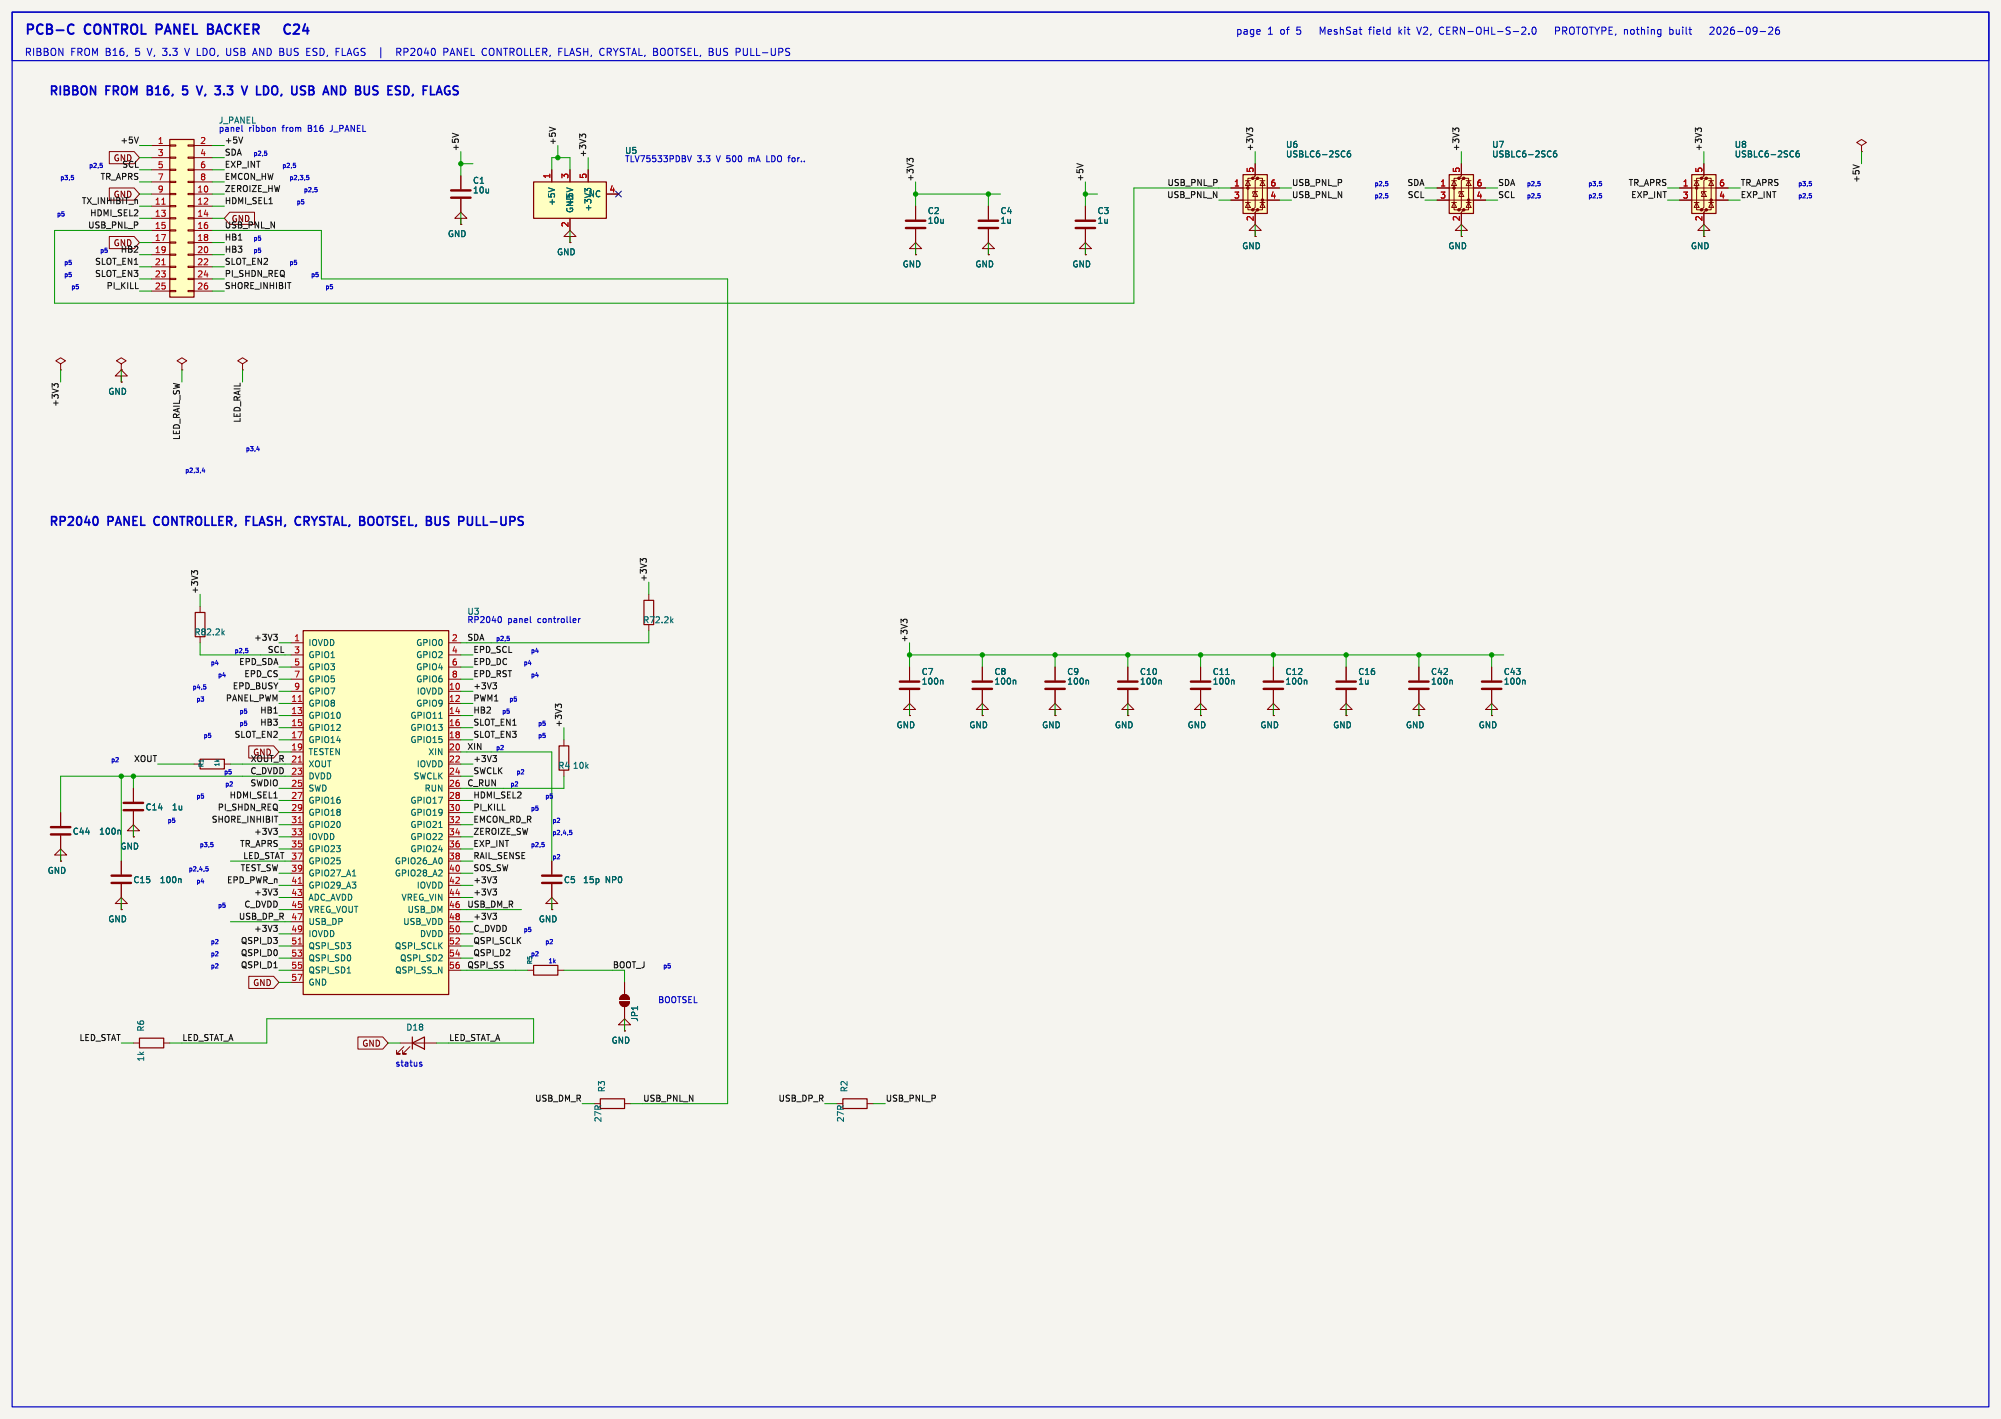
[picture p273: page 1]

RP2040 PANEL CONTROLLER, FLASH, CRYSTAL, BOOTSEL, BUS PULL-UPS

IOVDD 1 GPIO1 3 GPIO3 5 GPIO5 7 GPIO7 9 GPIO8 11 GPIO10 13 GPIO12 15 GPIO14 17 TESTEN 19 XOUT 21 DVDD 23 SWD 25 GPIO16 27 GPIO18 29 GPIO20 31

GND R⁴⁰ 300R R³³ 180R D³

p5 | PCA9555PW 0x22 EXPANDERS 0x22 / 0x23, MODE INPUTS, EMCON AND ZEROIZE BUFFERS, STRAPS

# 3 GND

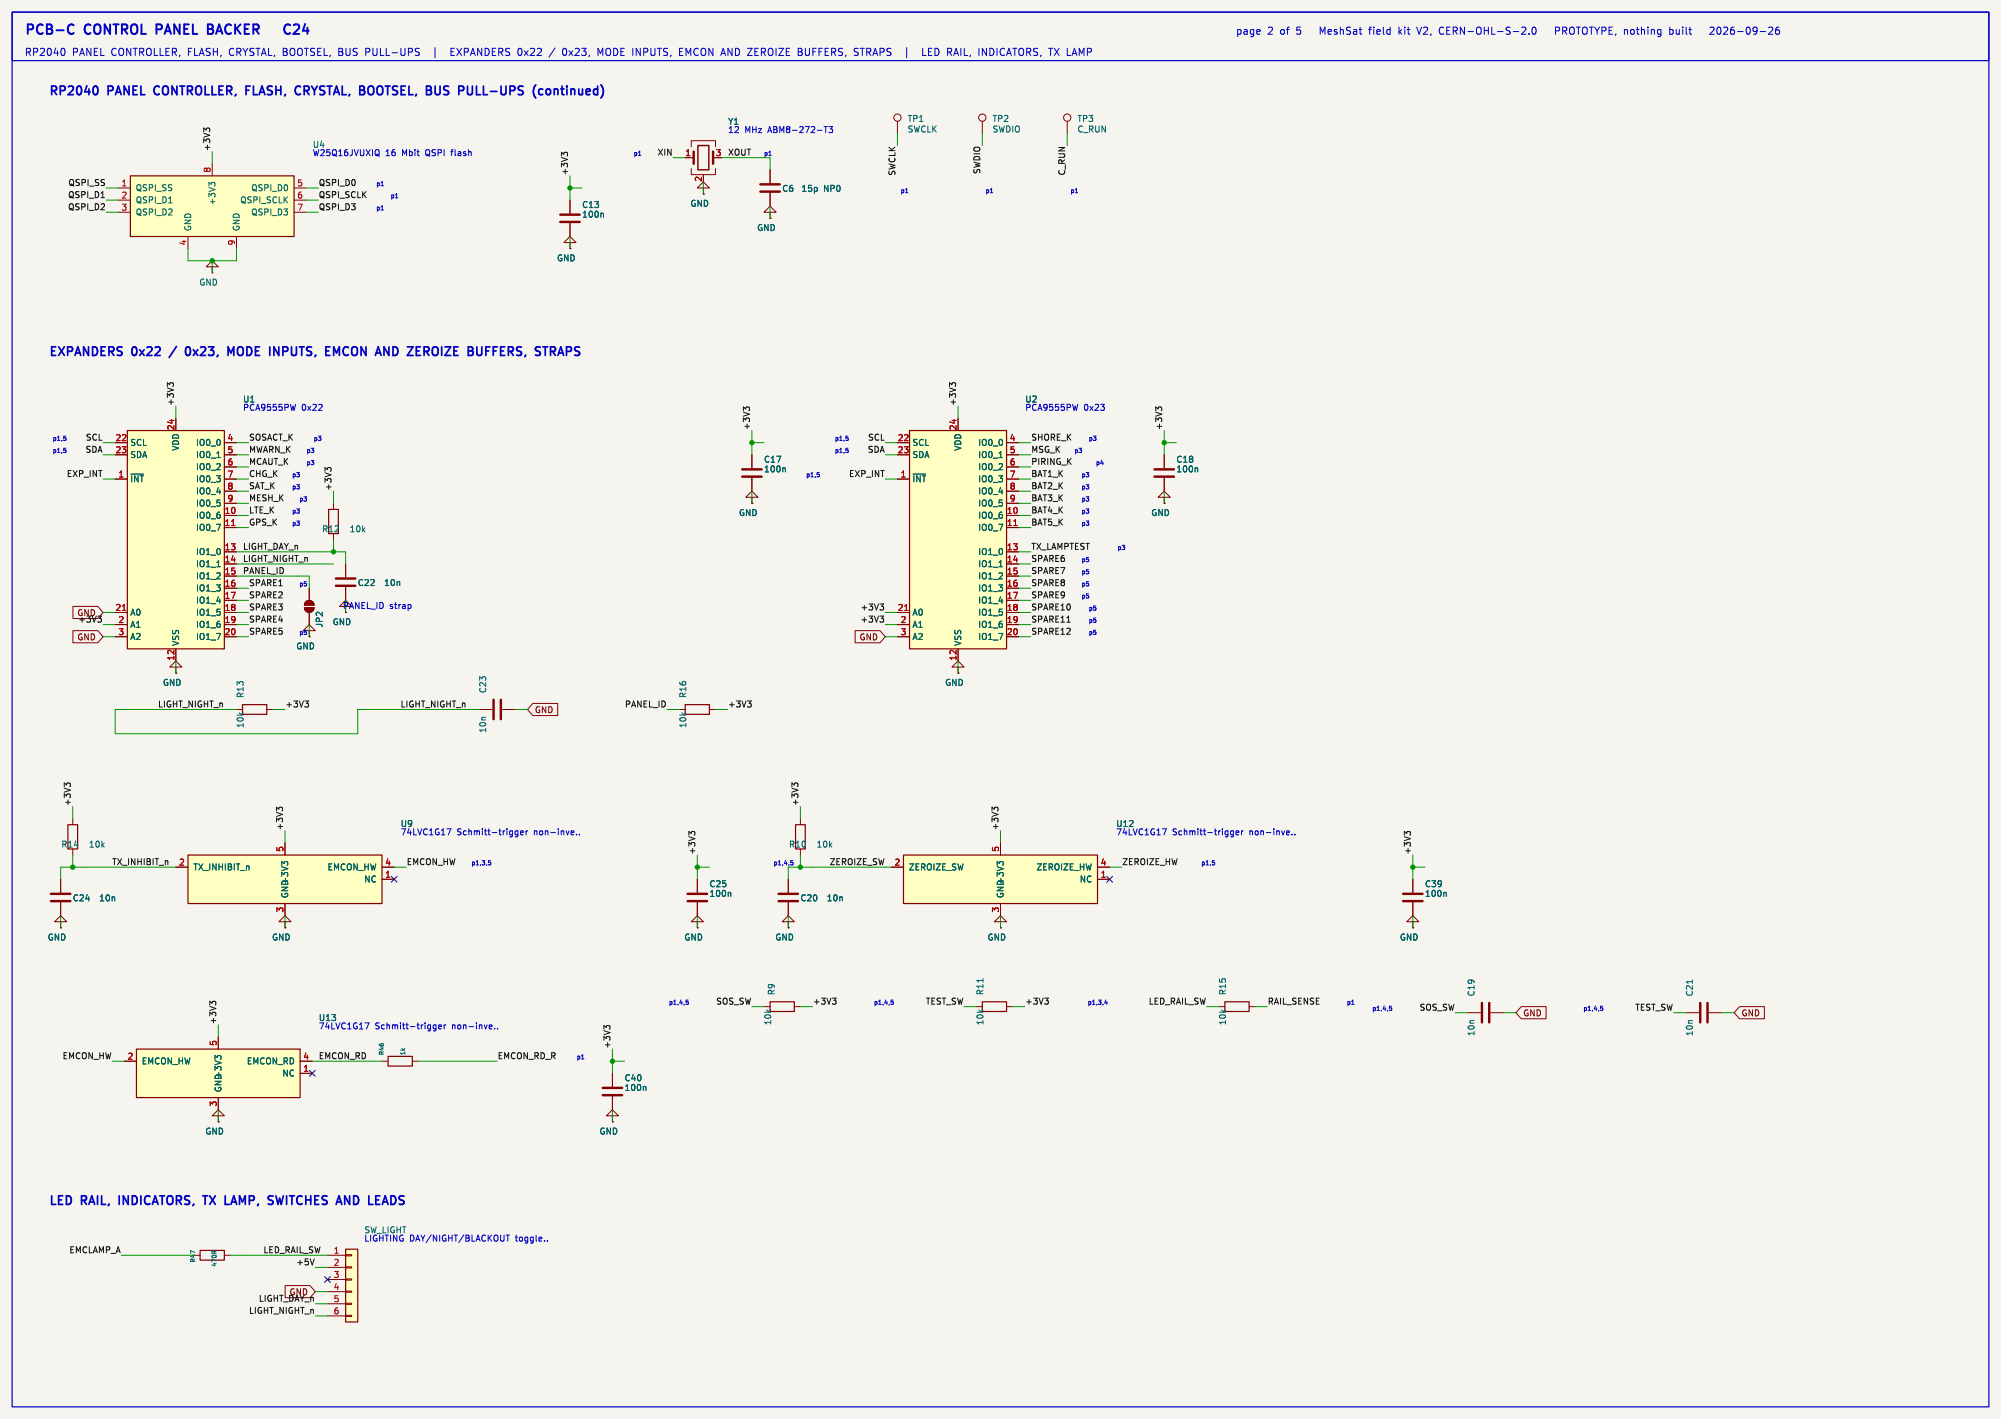
[picture p274: page 2]

GND | R¹⁶ 10k
TP30 HB3 | R¹¹ 10k

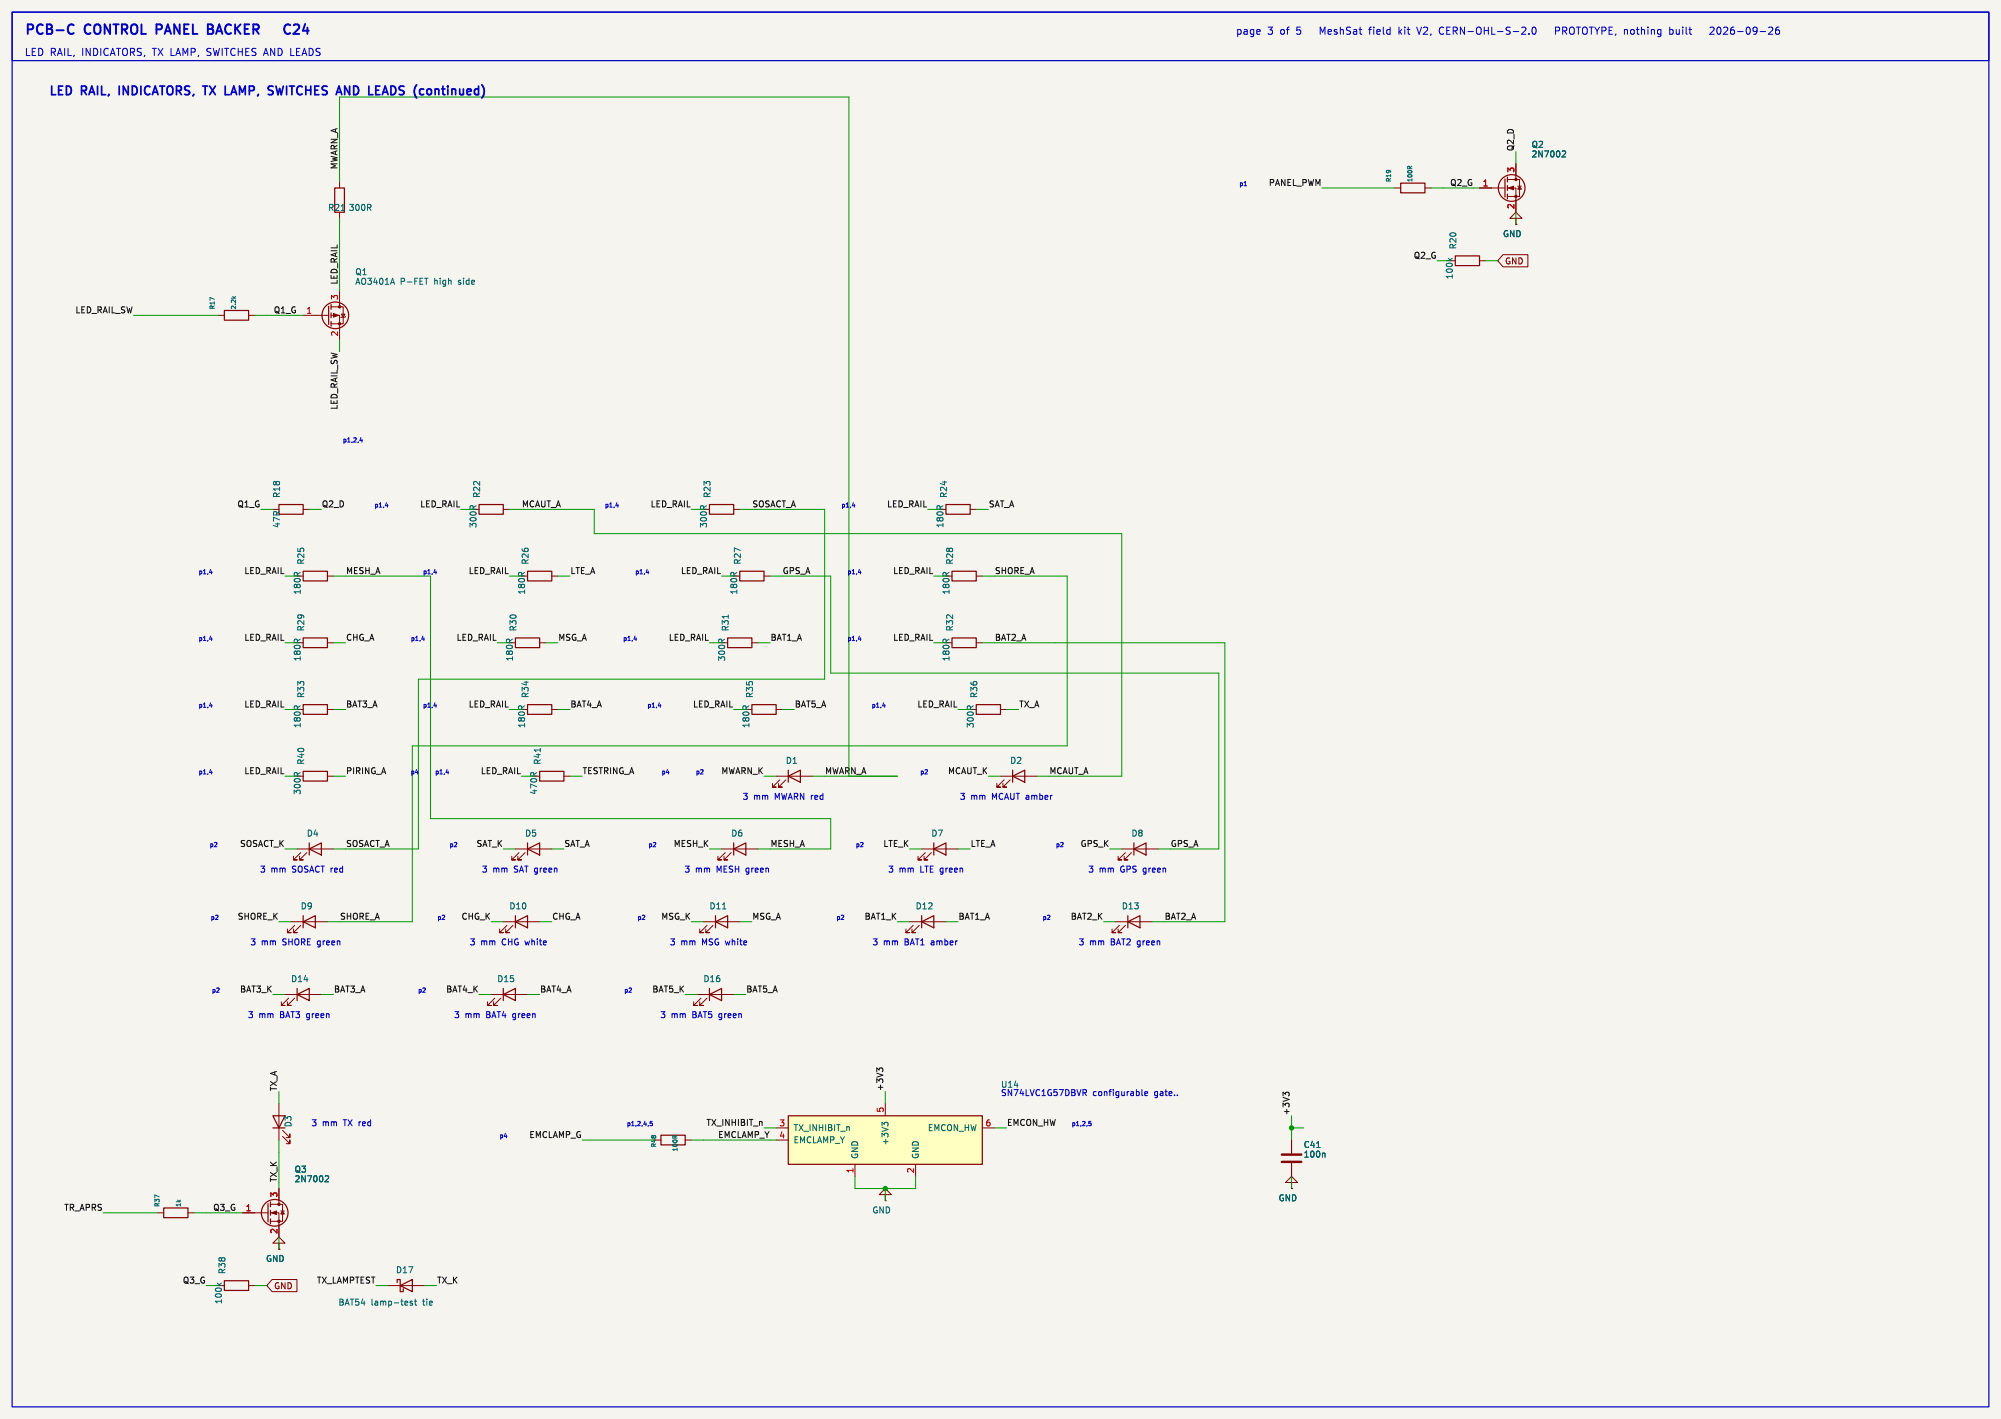
[picture p275: page 3]

TP2 SWDIO R²² 300R
GND R⁴⁰ 300R R³³ 180R D³

LED RAIL, INDICATORS, TX LAMP, SWITCHES AND LEADS (continued)

GND | R¹⁶ 10k
TP30 HB3 | R¹¹ 10k

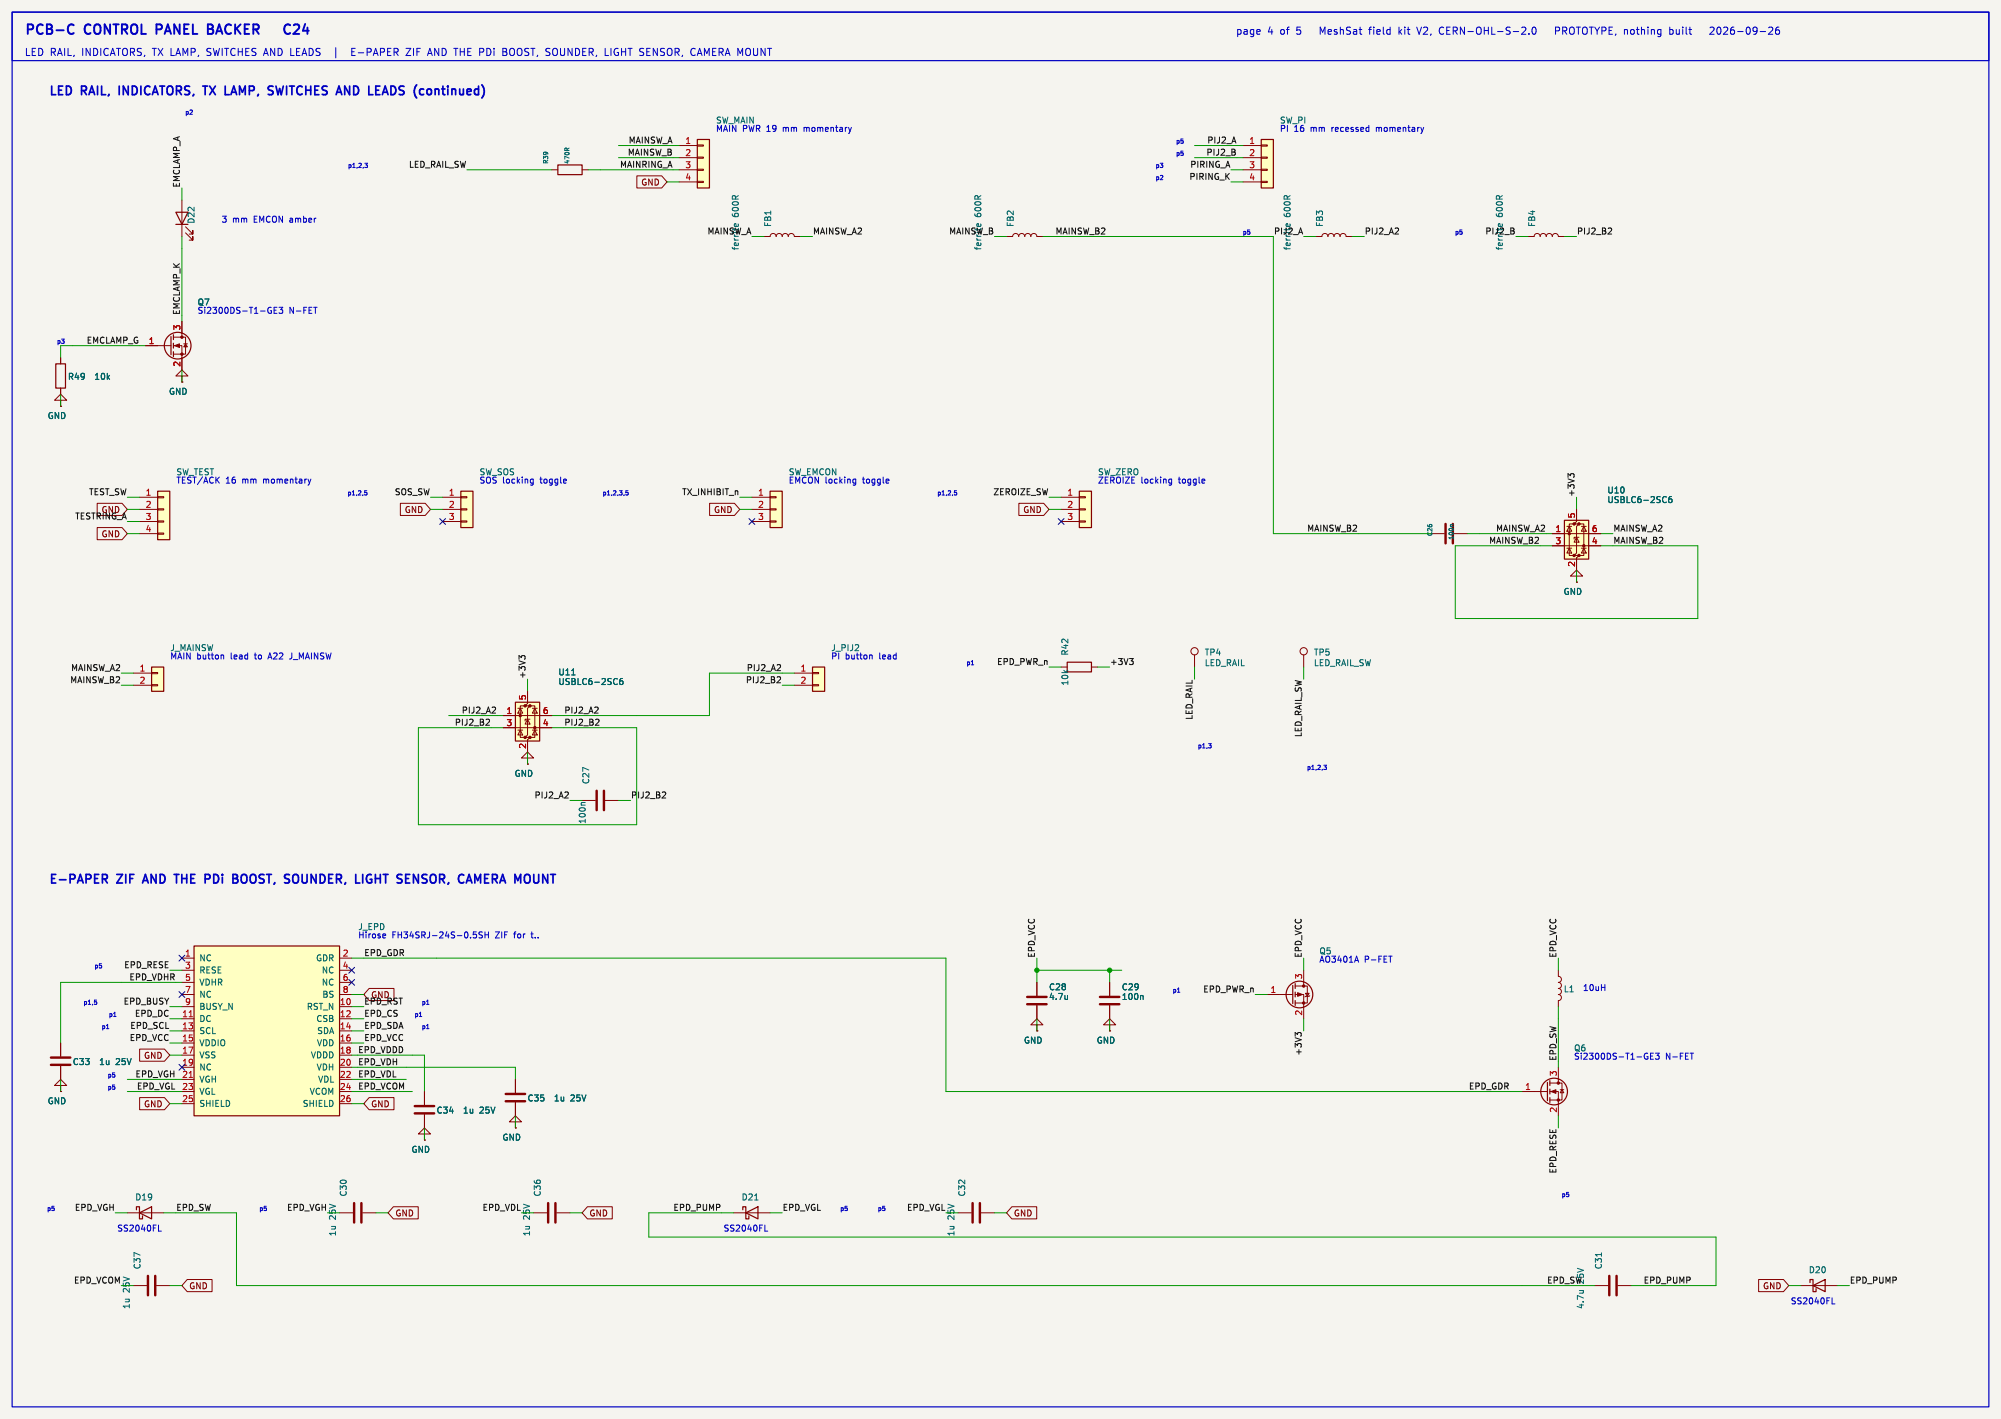
[picture p276: page 4]

LED RAIL, INDICATORS, TX LAMP, SWITCHES AND LEADS (continued)

MAIN PWR 19 mm momentary

PI 16 mm recessed momentary

TEST/ACK 16 mm momentary

E-PAPER ZIF AND THE PDi BOOST, SOUNDER, LIGHT SENSOR, CAMERA MOUNT

GND | R¹⁶ 10k
TP30 HB3 | R¹¹ 10k

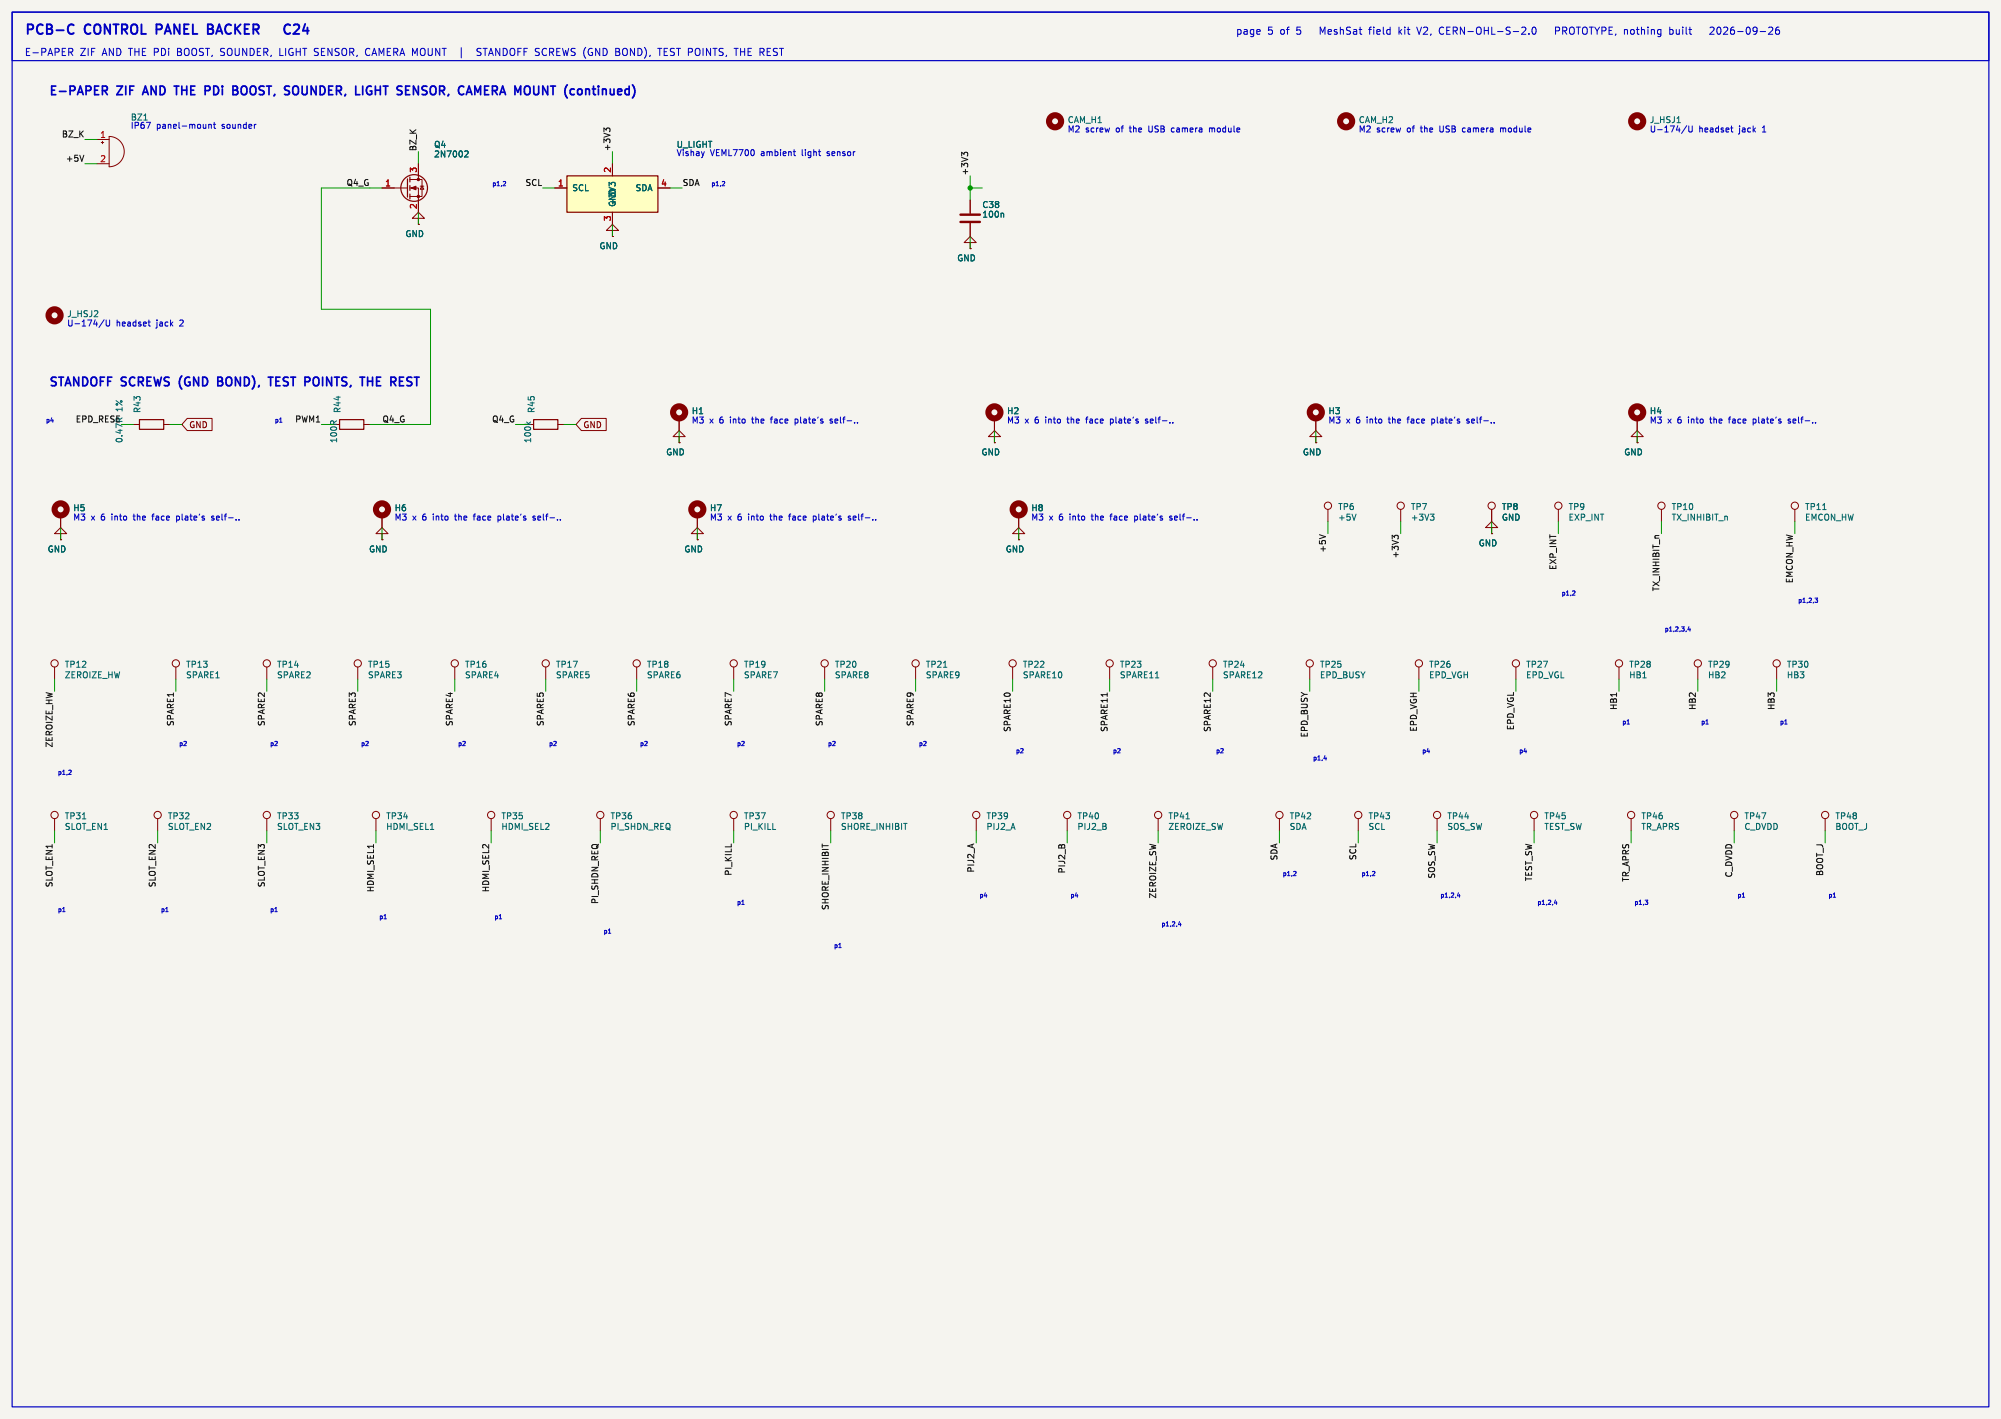
[picture p277: page 5]

p1,2 STANDOFF SCREWS (GND BOND), TEST POINTS, THE REST

M2 screw of the USB camera module
