meshsat/meshsat-fieldkit/v2/release/handover/H1/v2/release/handover/_generated/pcb-d-aprs-d9/pcb-d-aprs-schematic.pdf

# C1 GND R³⁶ 10k

C25 10u | C⁵ 47u 6.3V X⁵R ¹²¹⁰ PA_KEY 2 | +3V³

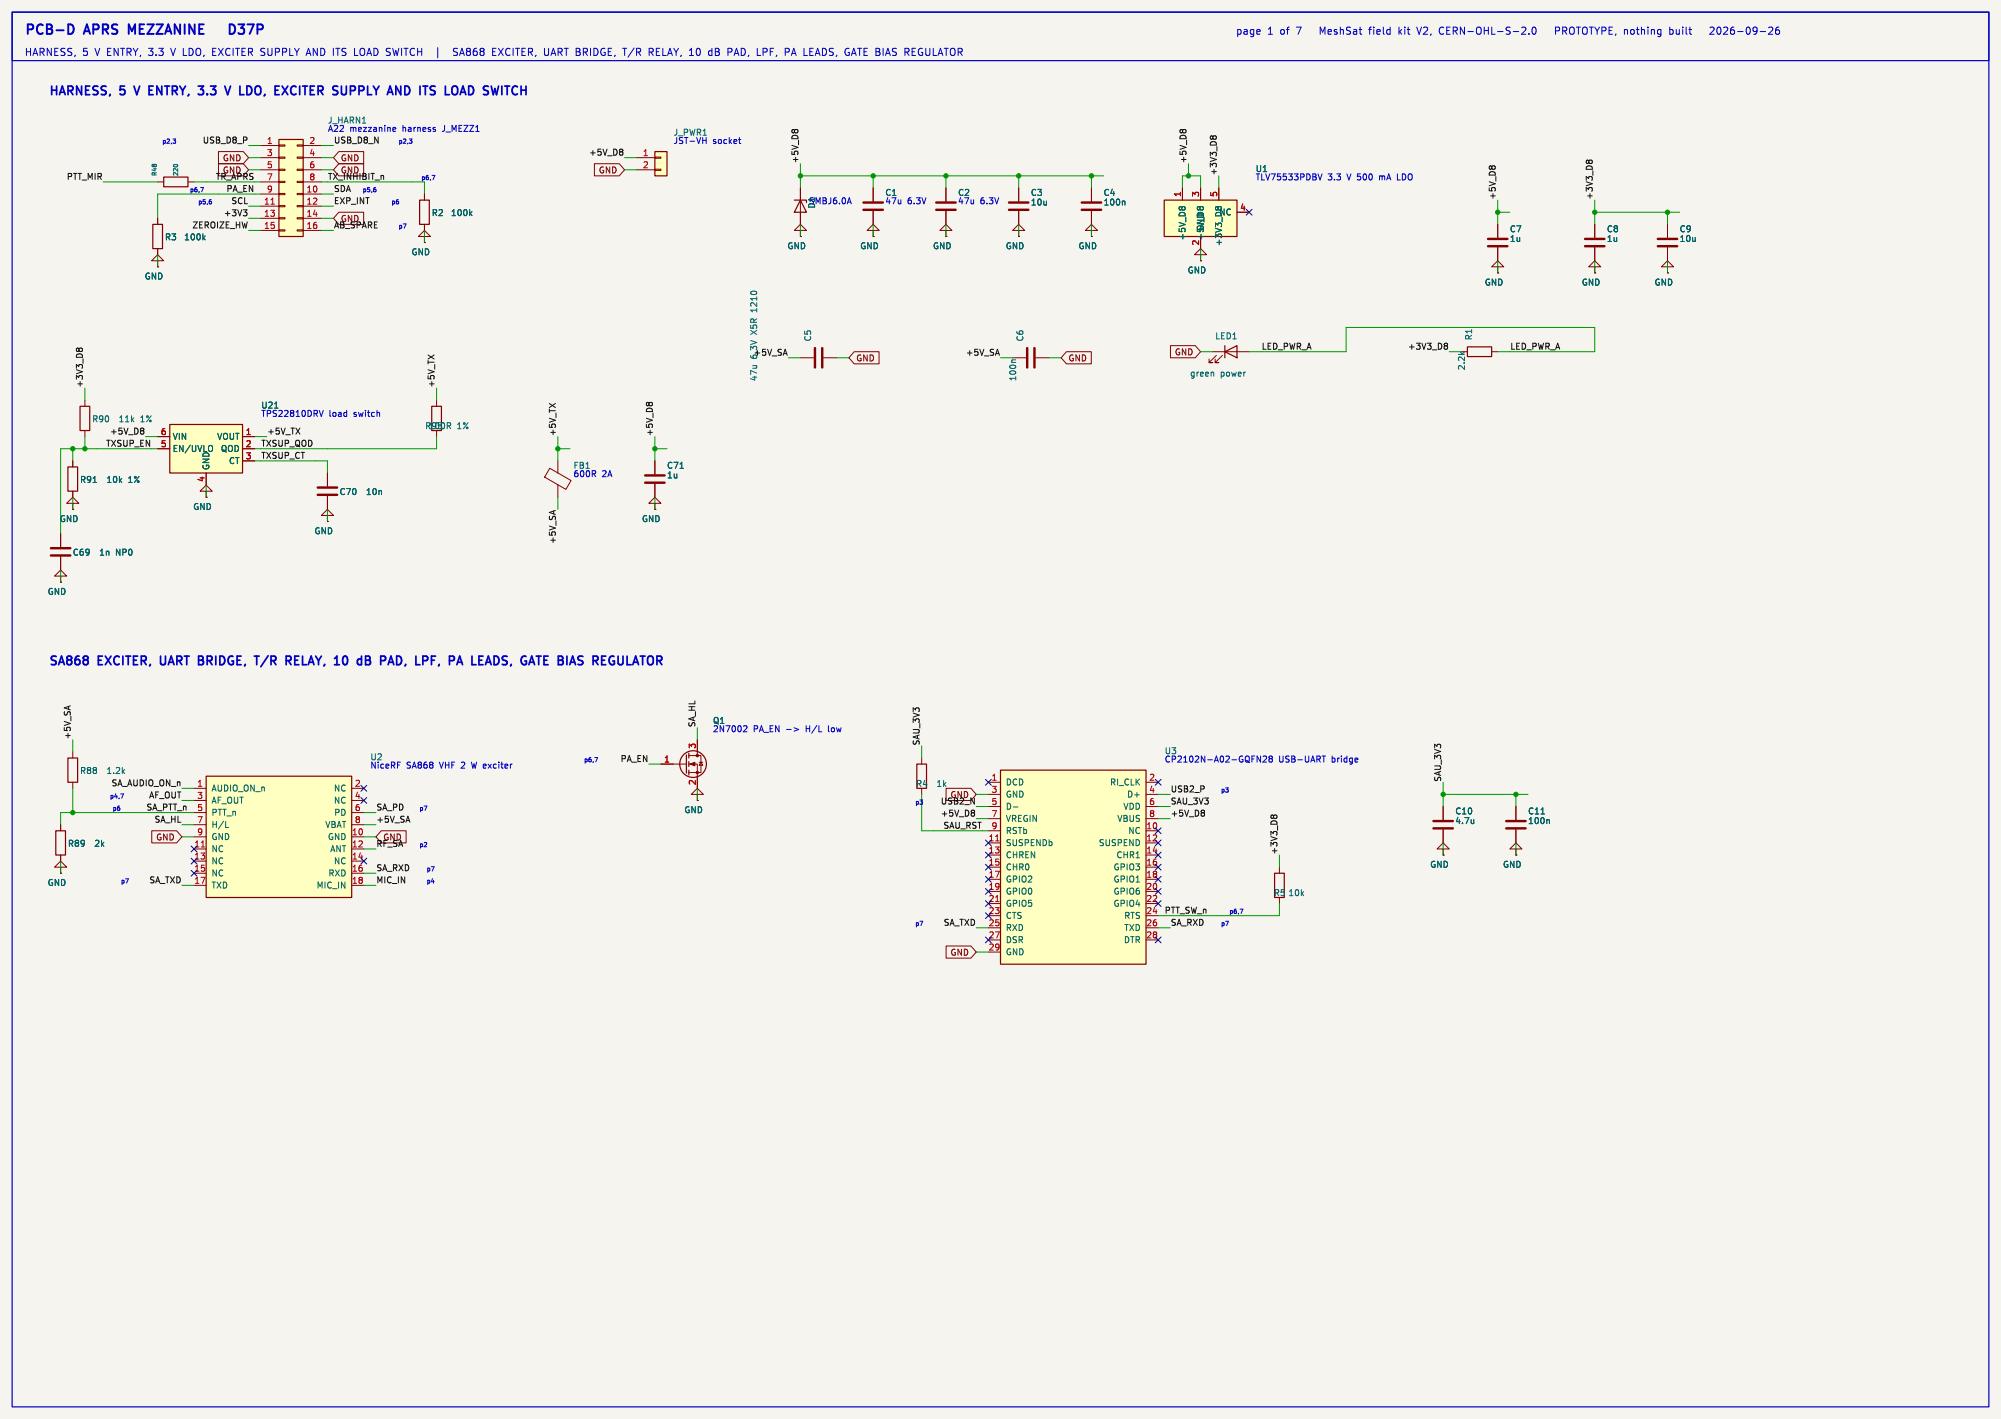
[picture p278: page 1]

p7 SA868 EXCITER, UART BRIDGE, T/R RELAY, 10 dB PAD, LPF, PA LEADS, GATE BIAS REGULATOR

# RF_ANT +3V³

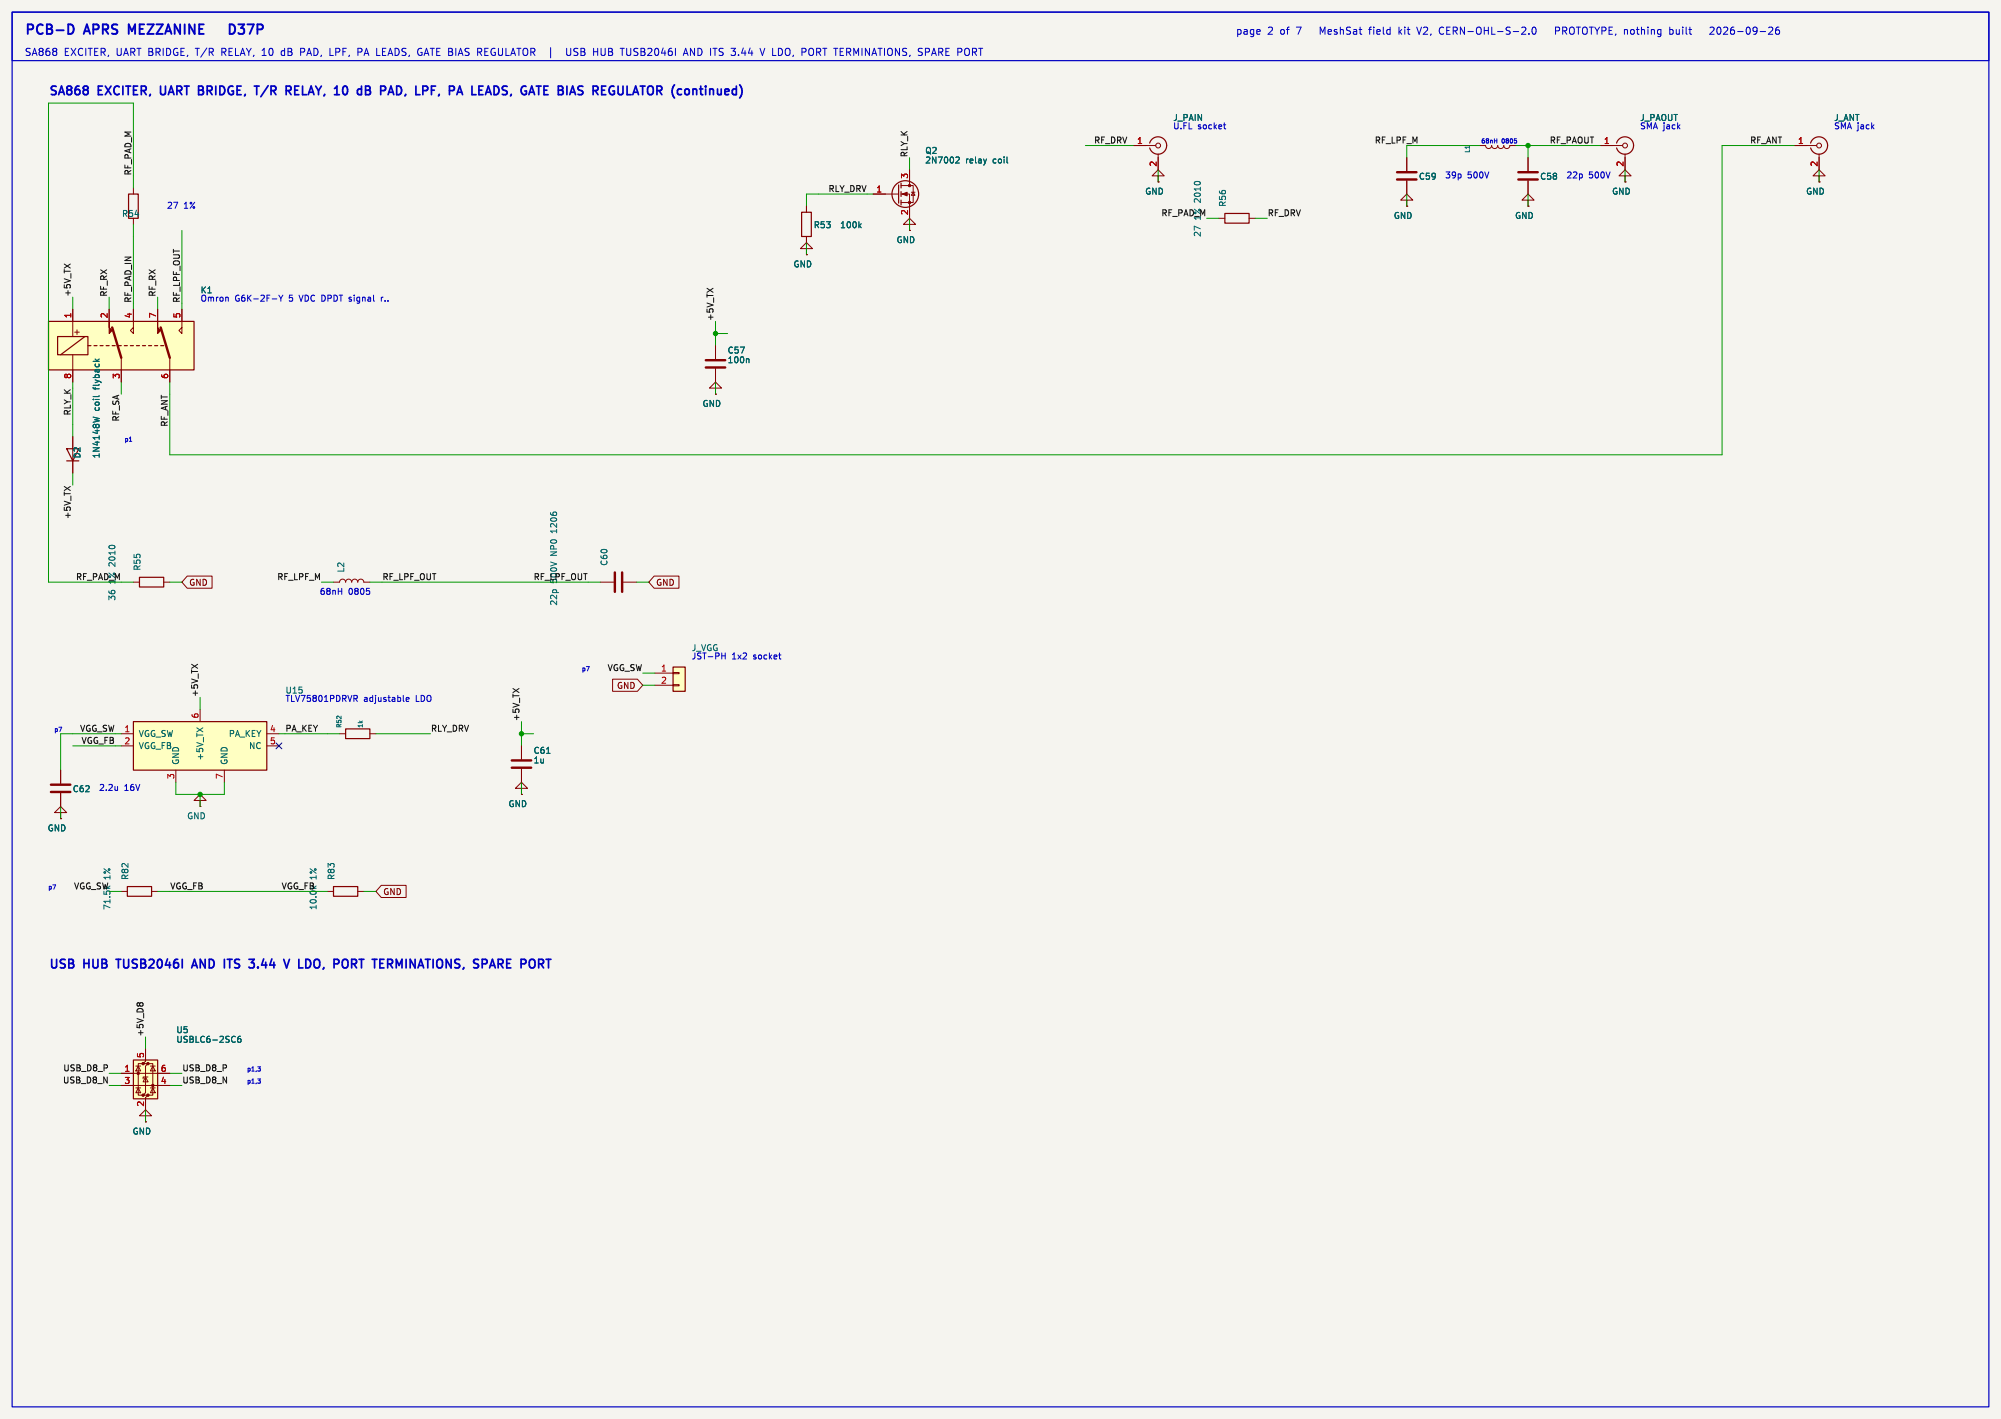
[picture p279: page 2]

2 GND GND GND GND GND

USB HUB TUSB2046I AND ITS 3.44 V LDO, PORT TERMINATIONS, SPARE PORT

GND R¹² | 22
R14 15k R⁴⁹ | 1k

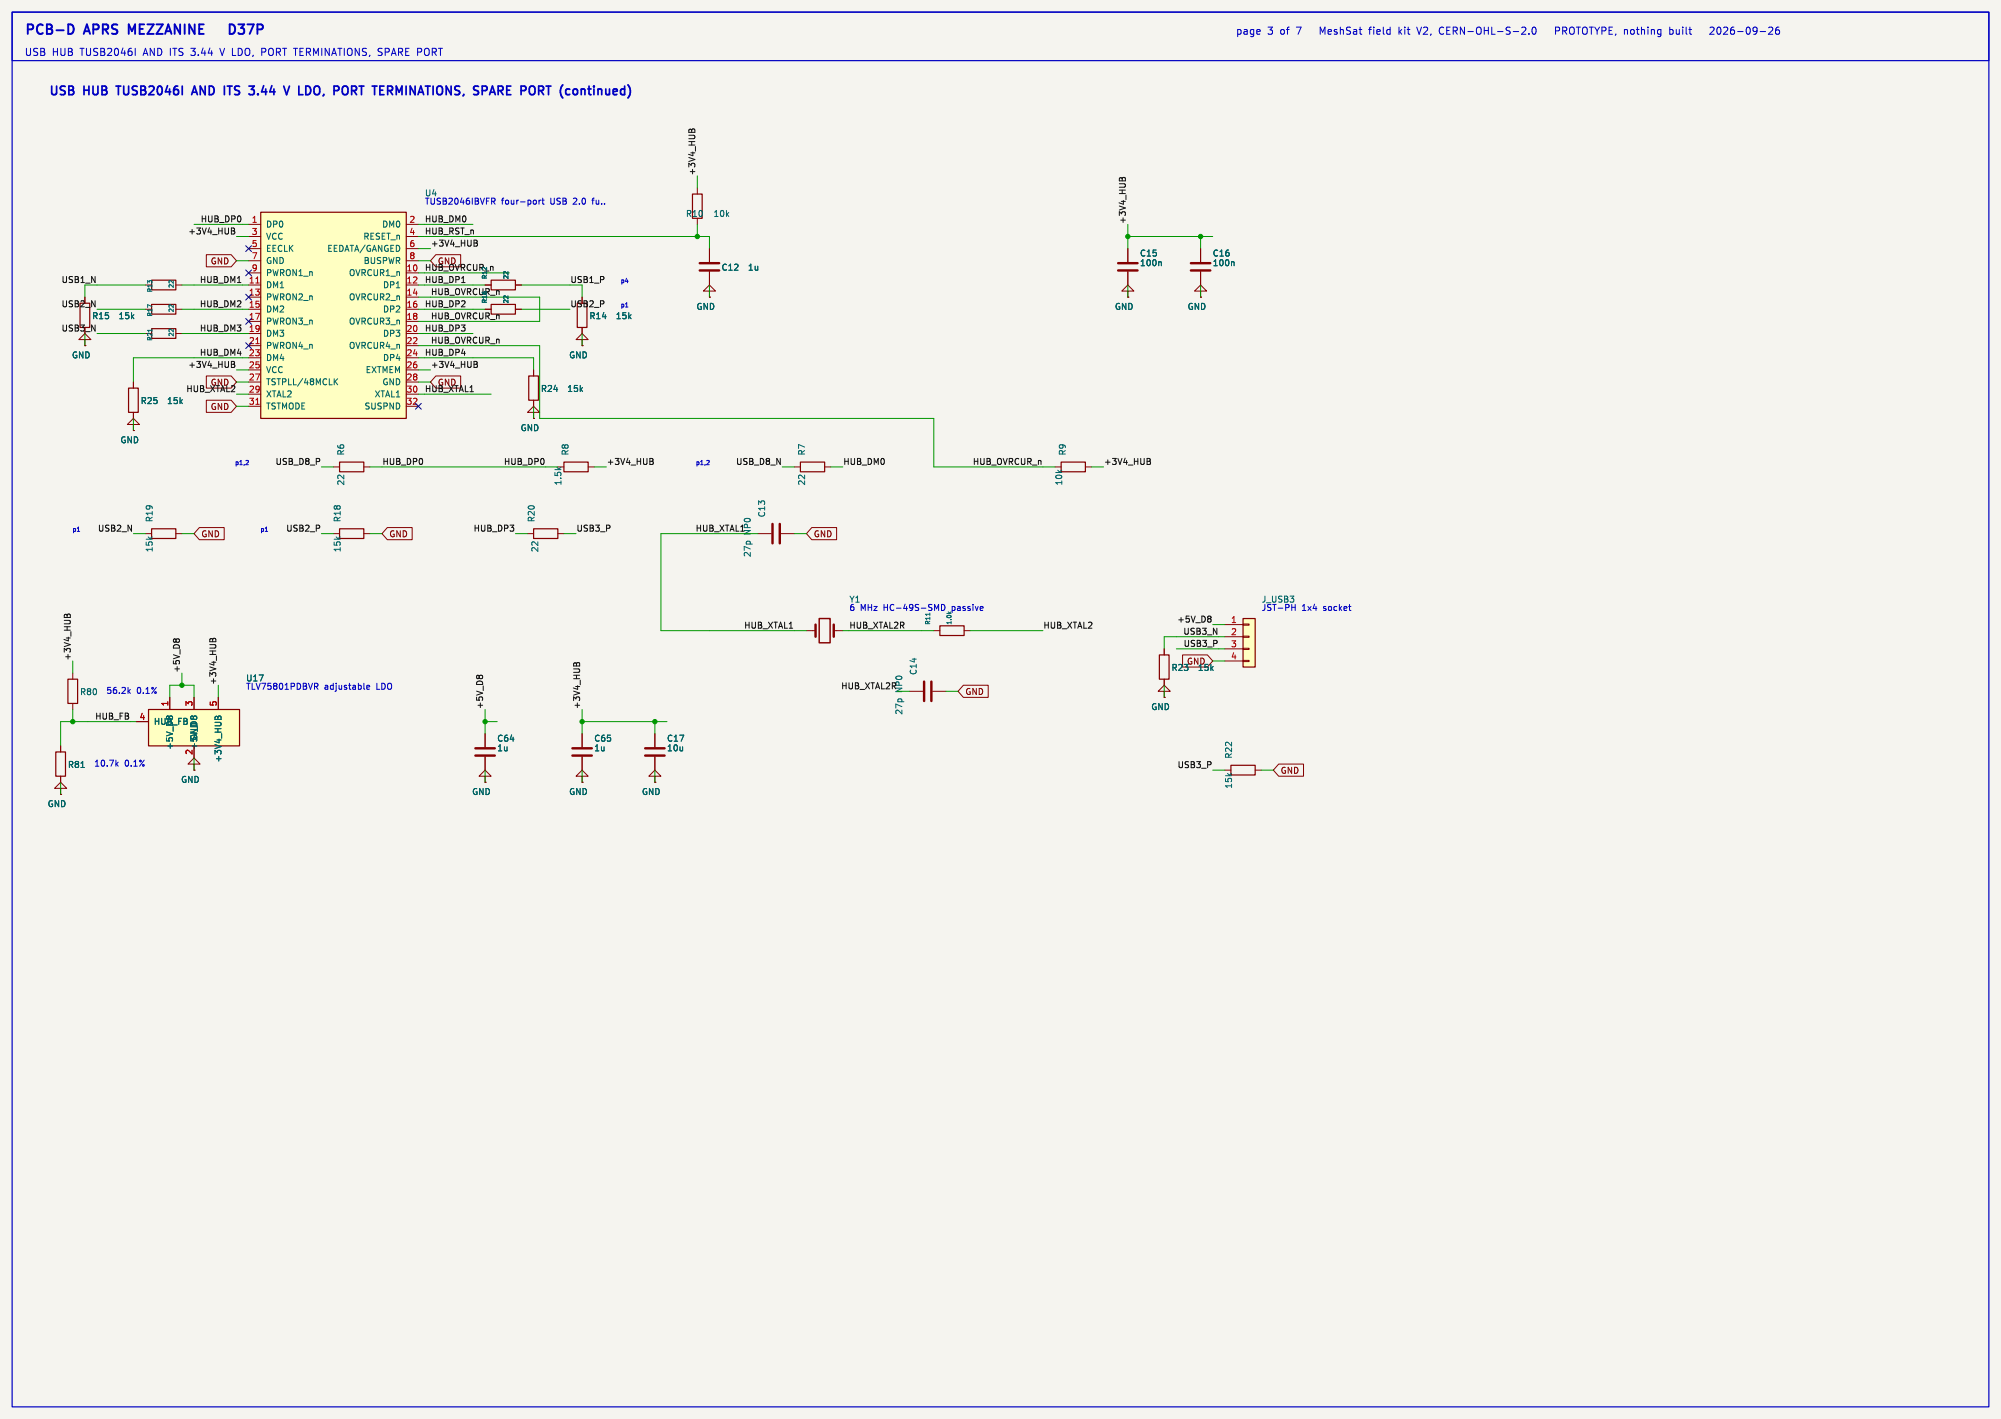
[picture p280: page 3]

2 GND GND GND GND GND

# C1 GND R³⁶ 10k

# GND GND

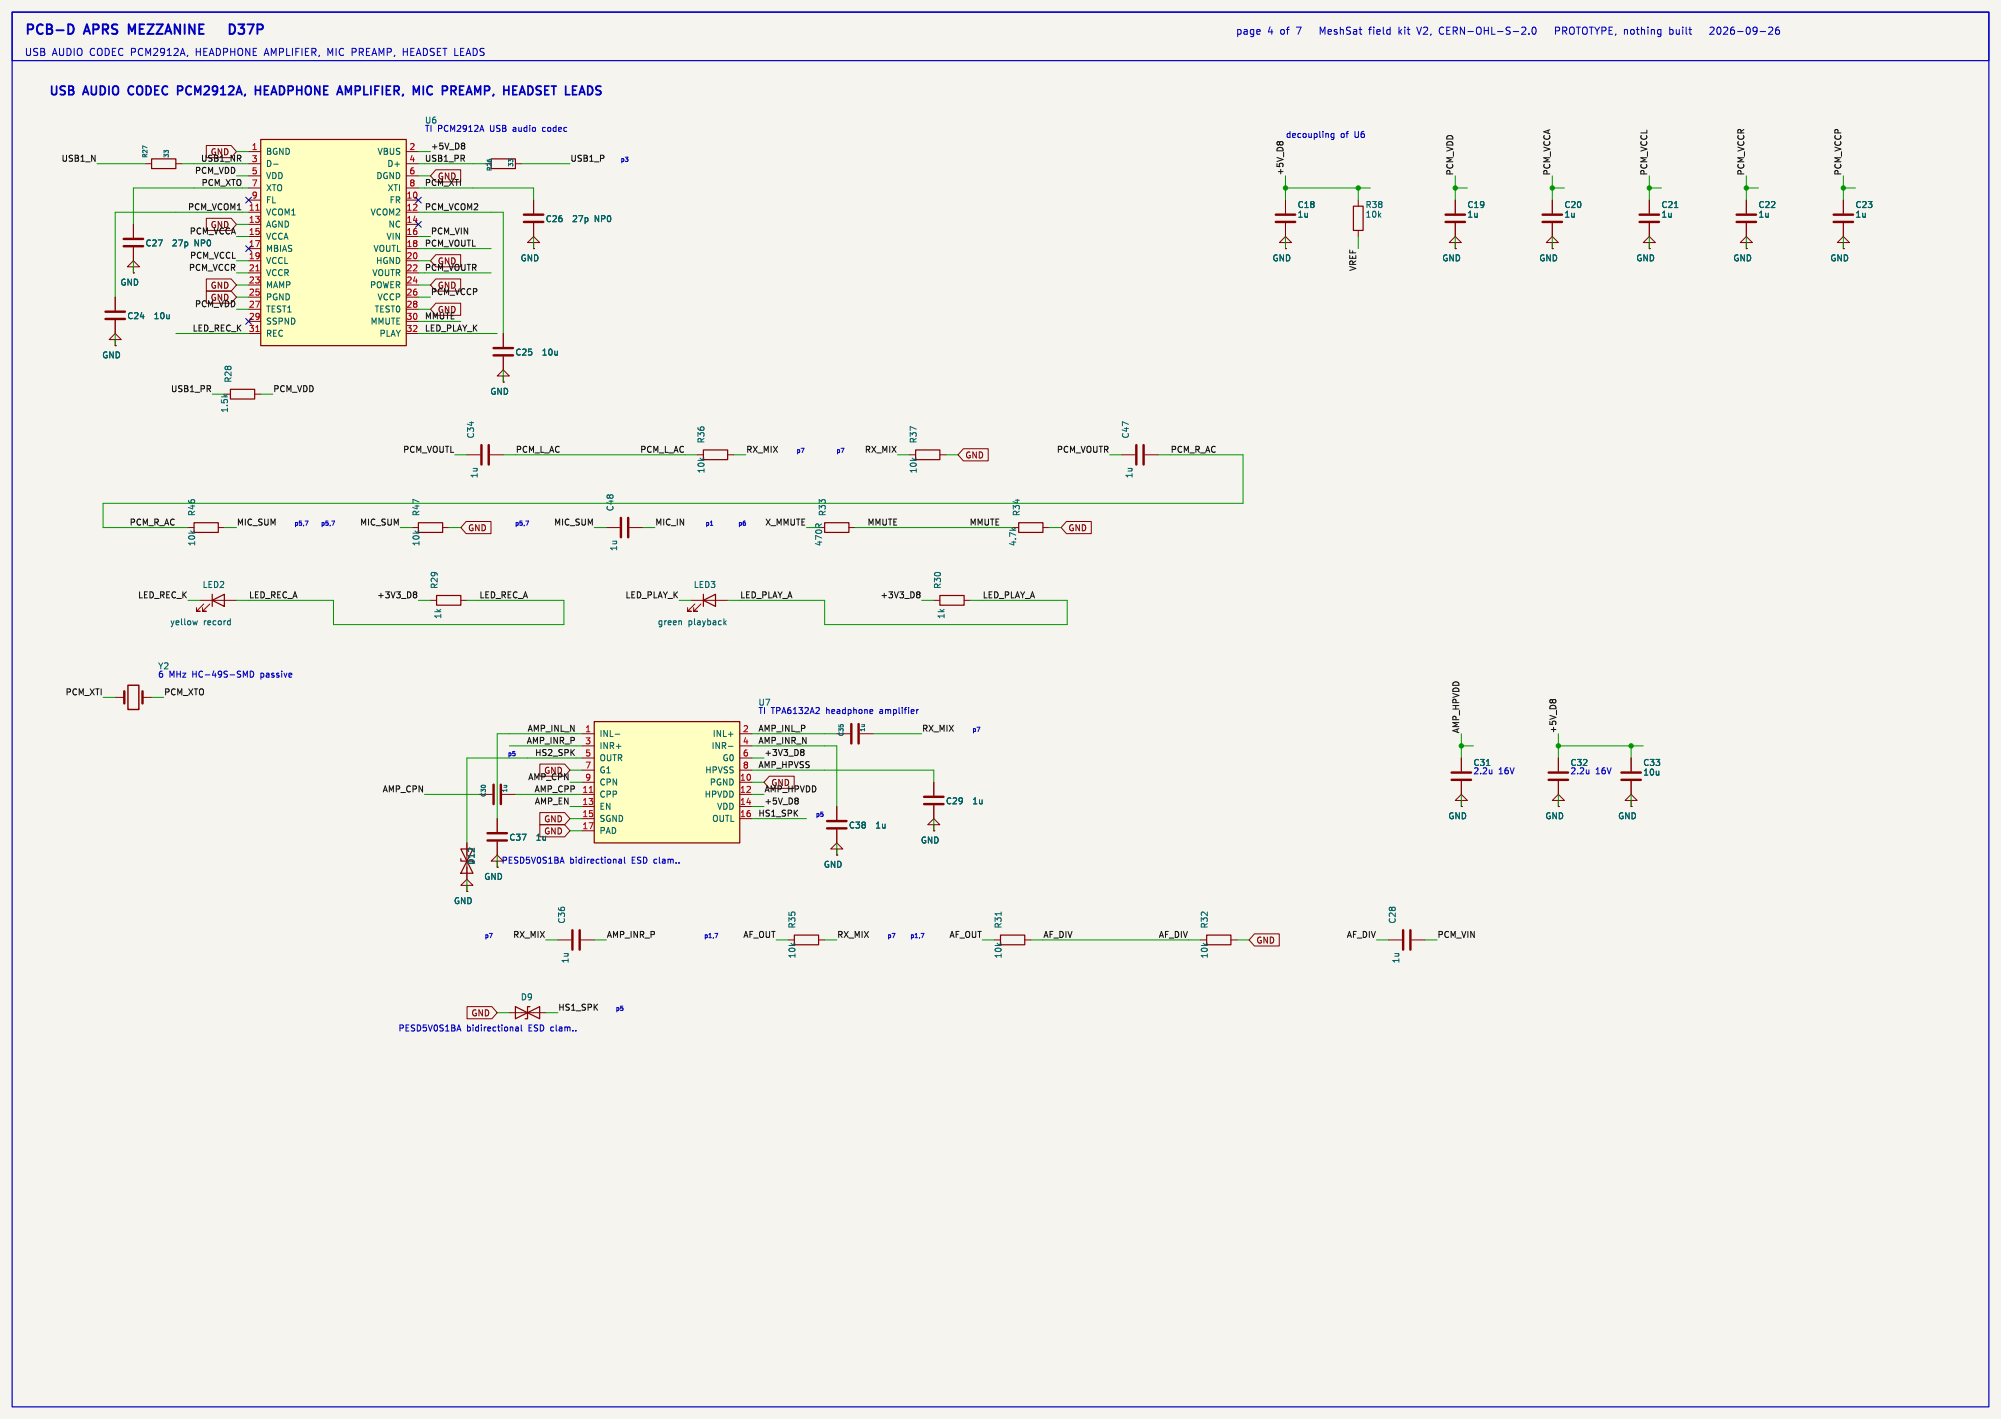
[picture p281: page 4]

USB AUDIO CODEC PCM2912A, HEADPHONE AMPLIFIER, MIC PREAMP, HEADSET LEADS

INR+ 3 OUTR 5 G1 7 CPN 9 CPP 11 EN 13 SGND 15 PAD 17

7 U8

# USB_D8_N VREF

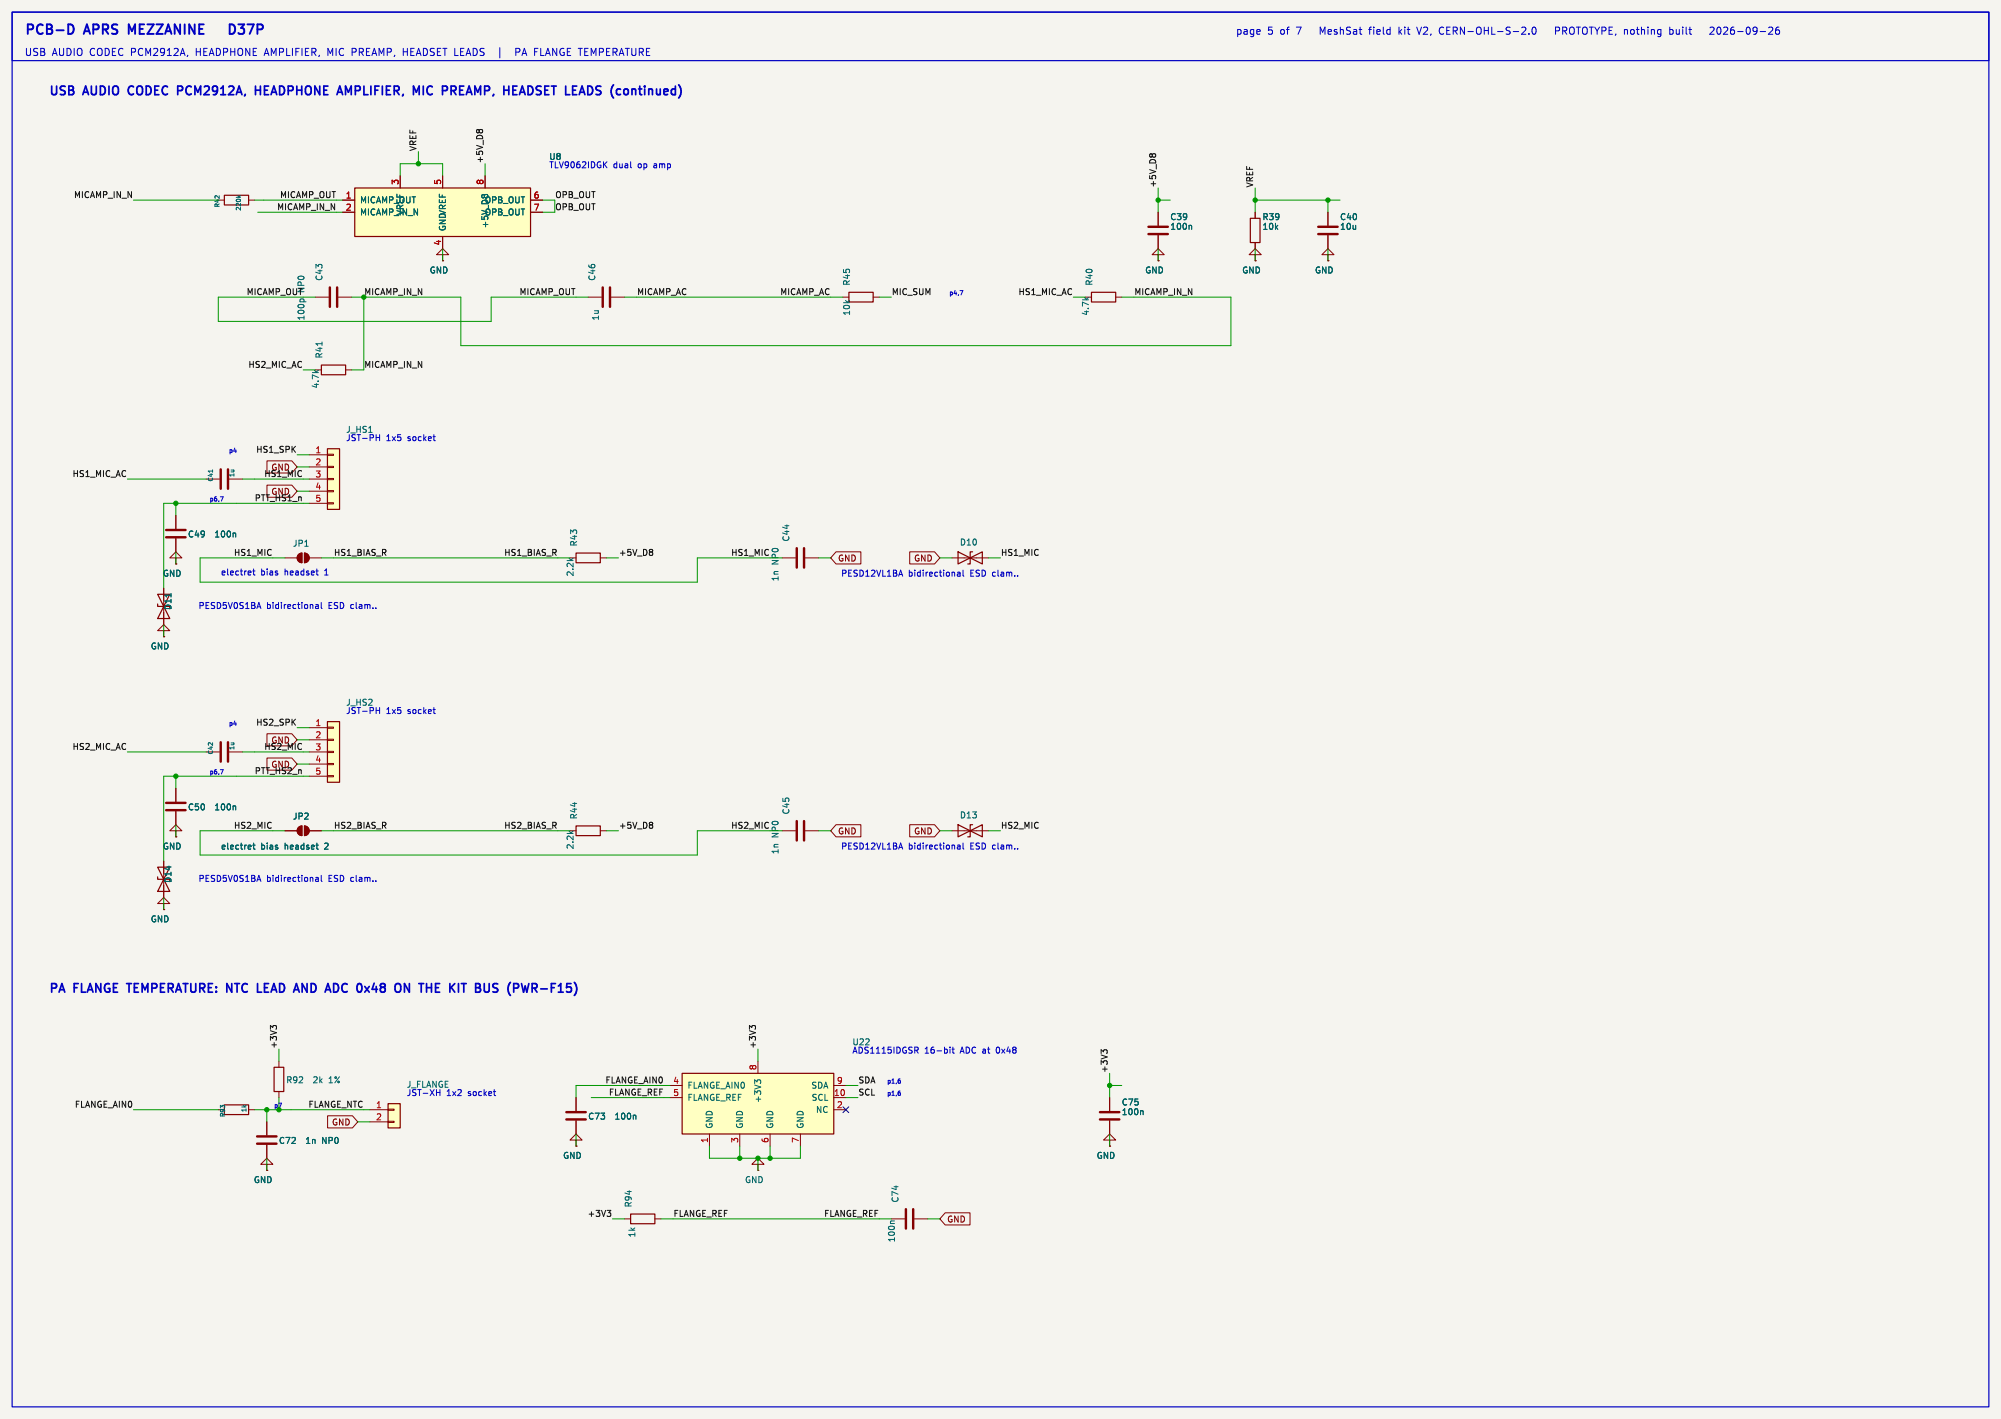
[picture p282: page 5]

USB AUDIO CODEC PCM2912A, HEADPHONE AMPLIFIER, MIC PREAMP, HEADSET LEADS (continued)

GND GND

PA FLANGE TEMPERATURE: NTC LEAD AND ADC 0x48 ON THE KIT BUS (PWR-F15)

GND R¹² | 22
R14 15k R⁴⁹ | 1k

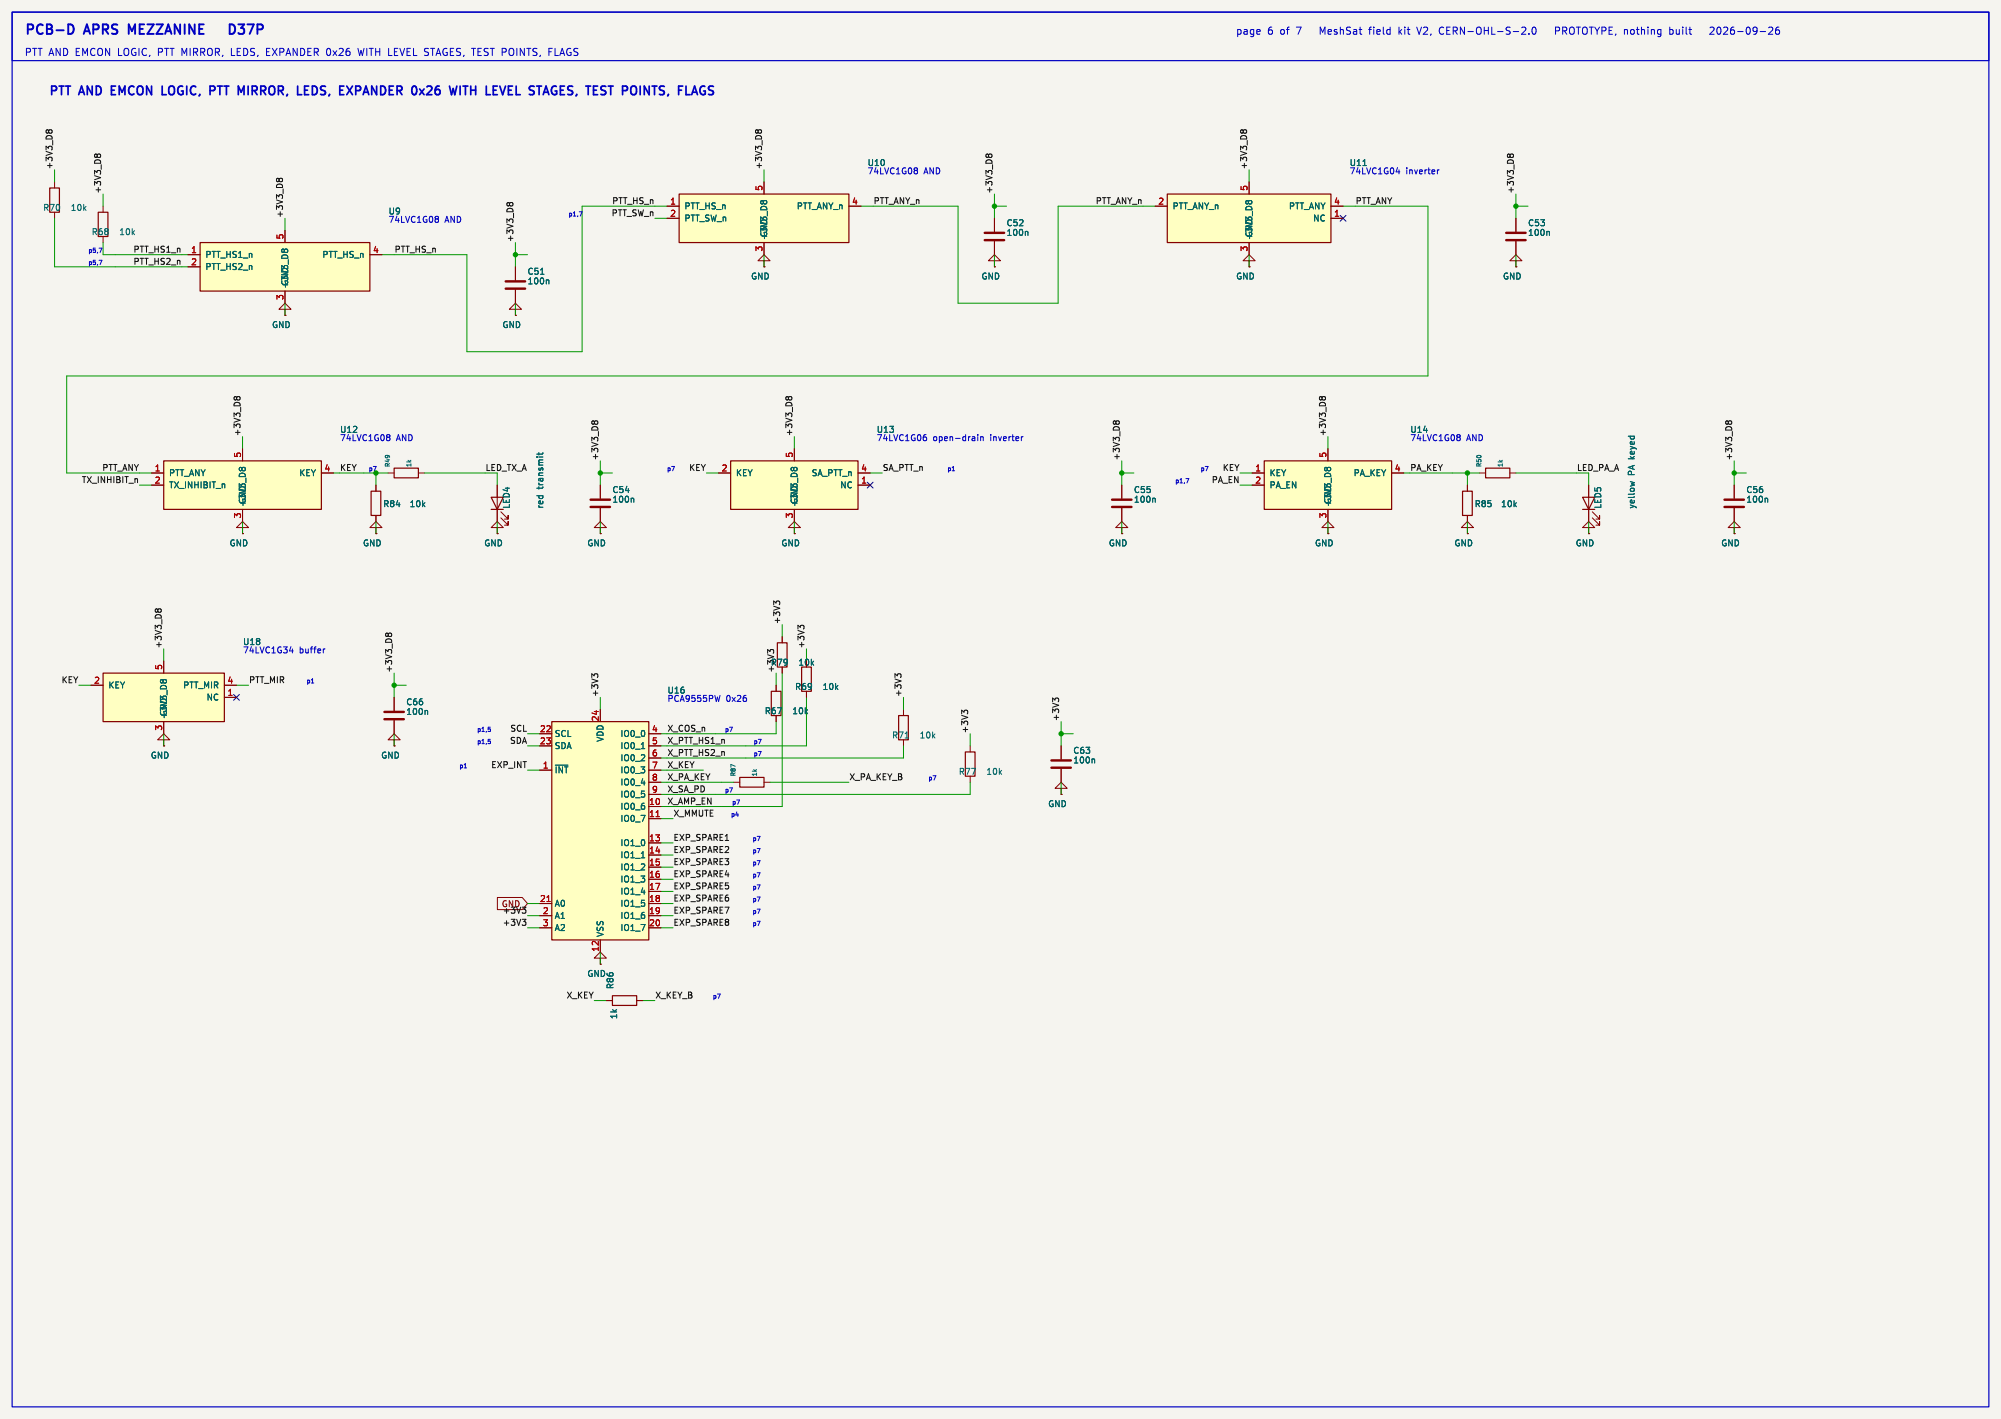
[picture p283: page 6]

PTT AND EMCON LOGIC, PTT MIRROR, LEDS, EXPANDER 0x26 WITH LEVEL STAGES, TEST POINTS, FLAGS PTT AND EMCON LOGIC, PTT MIRROR, LEDS, EXPANDER 0x26 WITH LEVEL STAGES, TEST POINTS, FLAGS

C25 10u | C⁵ 47u 6.3V X⁵R ¹²¹⁰ PA_KEY 2 | +3V³
2N7002 | R²⁸ 1.5k

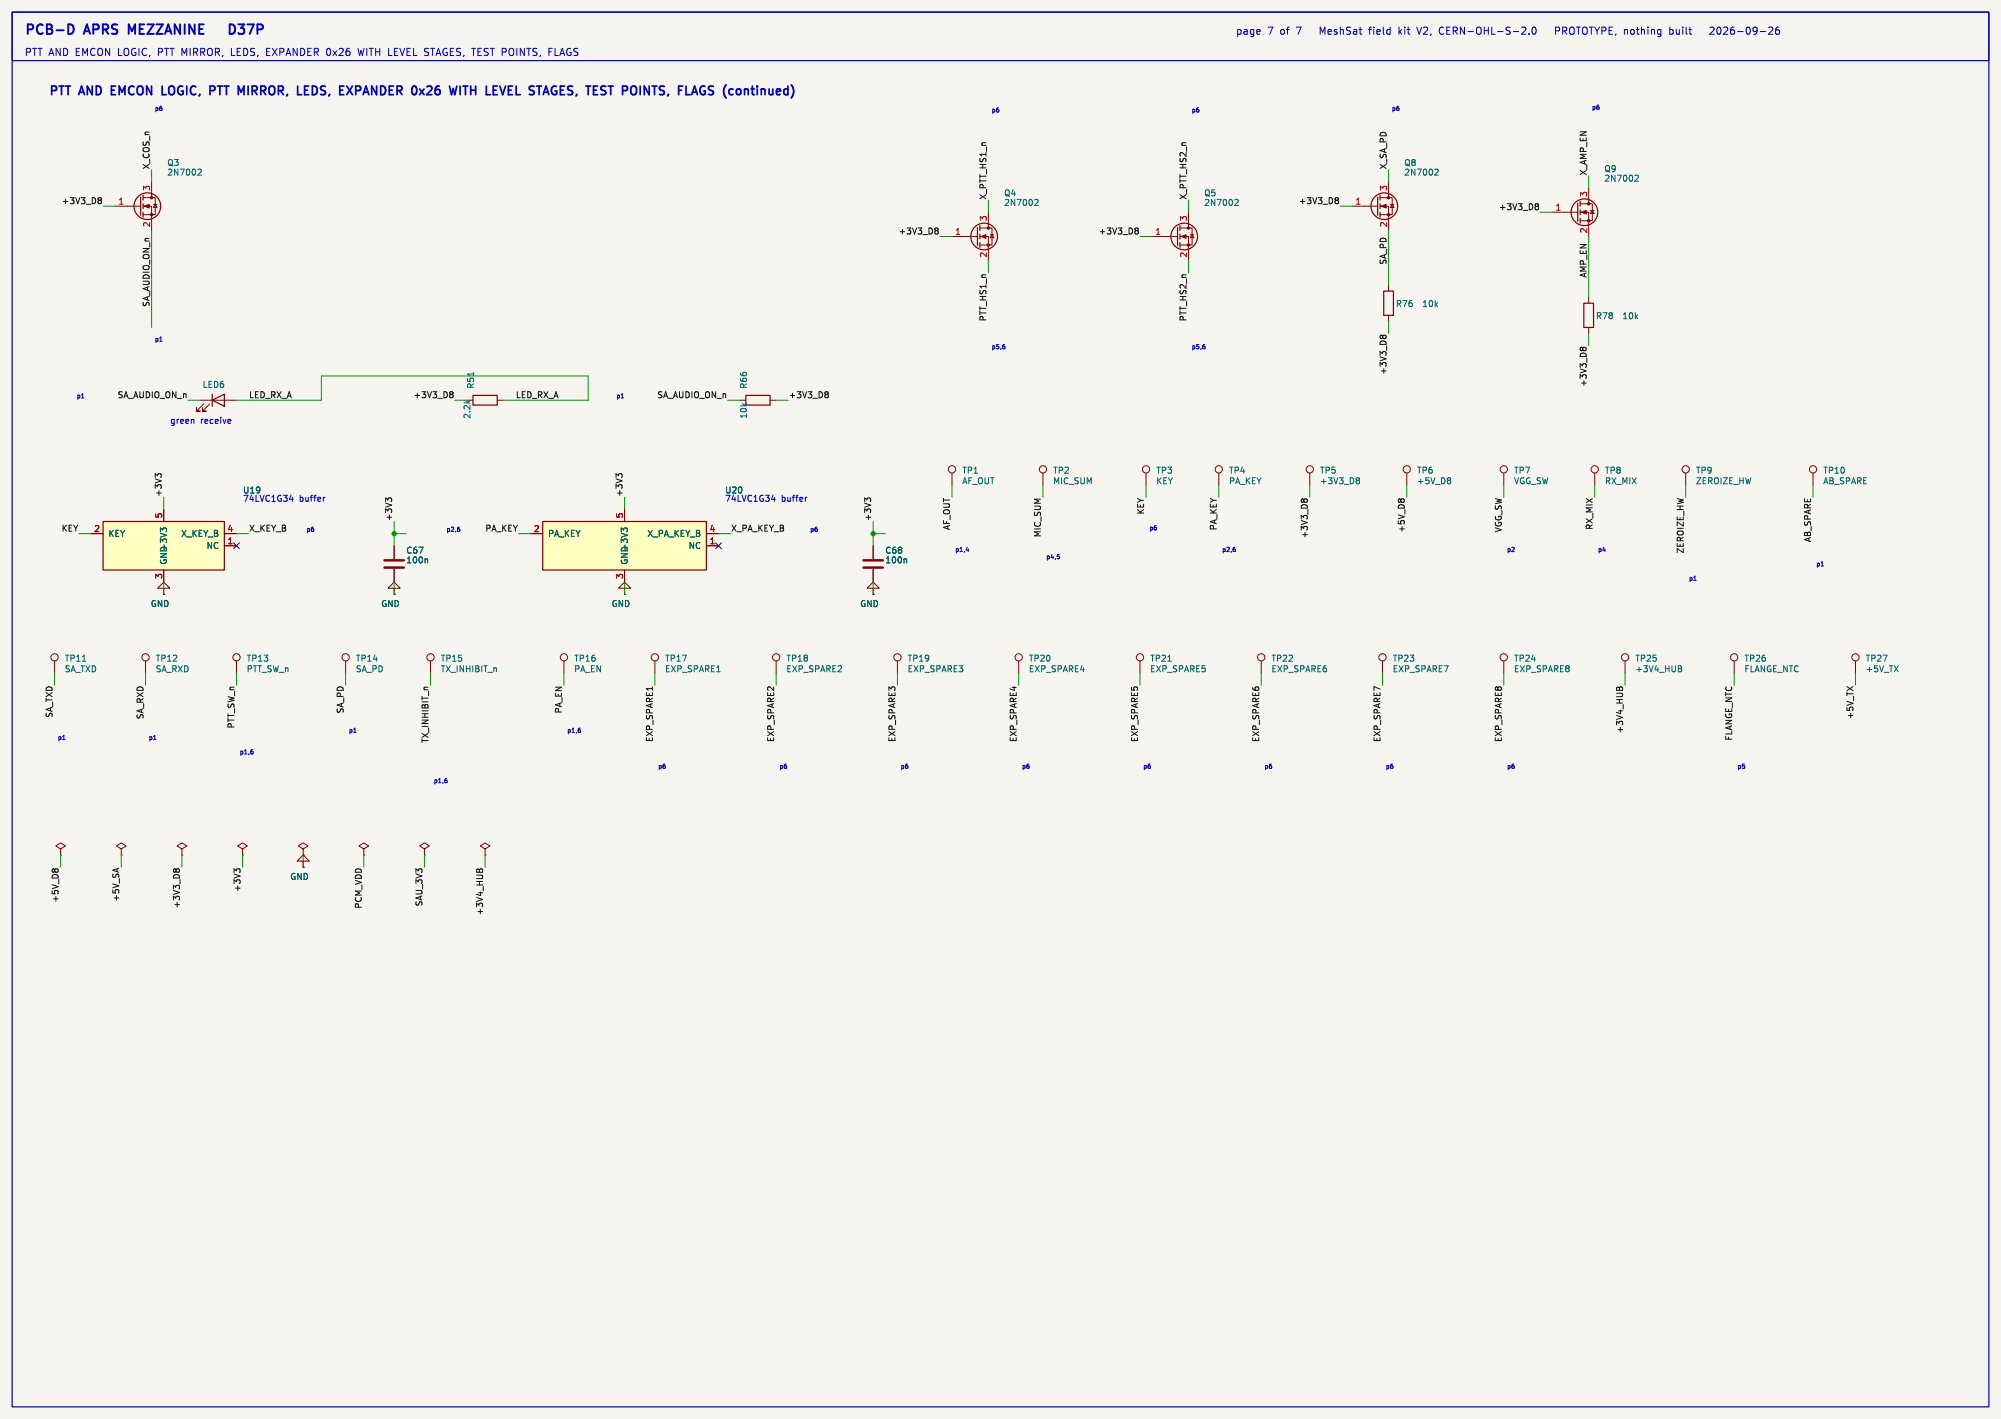
[picture p284: page 7]

PTT AND EMCON LOGIC, PTT MIRROR, LEDS, EXPANDER 0x26 WITH LEVEL STAGES, TEST POINTS, FLAGS PTT AND EMCON LOGIC, PTT MIRROR, LEDS, EXPANDER 0x26 WITH LEVEL STAGES, TEST POINTS, FLAGS (continued)
