meshsat/meshsat-fieldkit/v2/release/handover/H1/v2/release/handover/_generated/pcb-e1-dock-e7/pcb-e1-dock-schematic.pdf

DC_P GND_V | DC_HS DC_HS DC_HS +3V³_E⁶ | CELL_F

p4 25 A

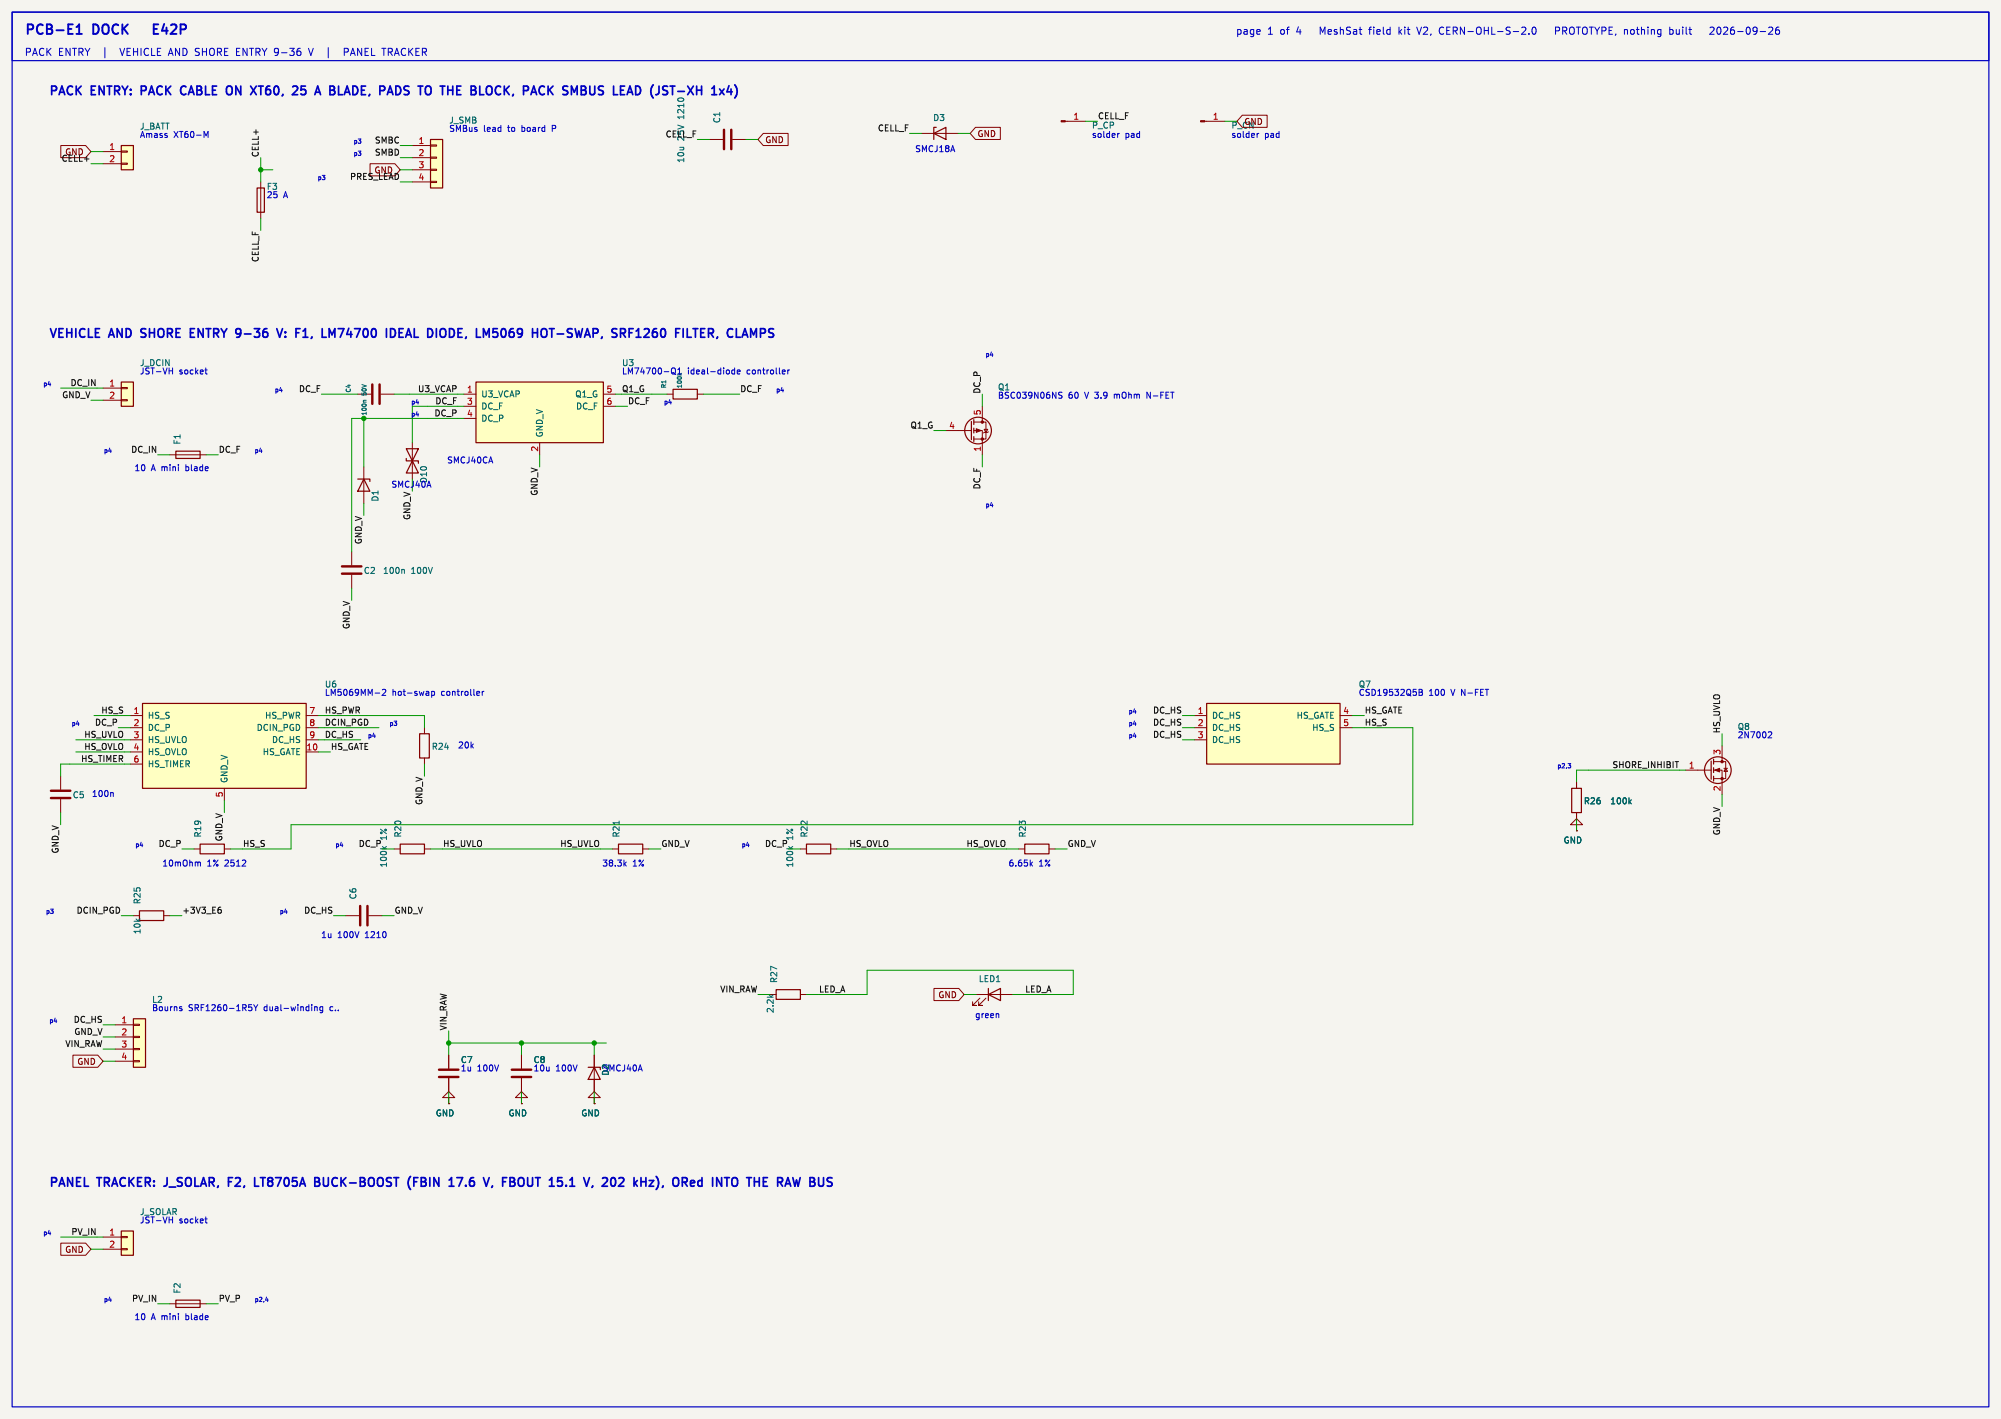
[picture p285: page 1]

J_SMB
SMBus lead to board P

p3 PANEL TRACKER: J_SOLAR, F2, LT8705A BUCK-BOOST (FBIN 17.6 V, FBOUT 15.1 V, 202 kHz), ORed INTO THE RAW BUS

R17 10k R⁶ | 10R | 4
C12C¹⁸ 470n 25V | C15 4.7u 50V GND R¹³ 10k C¹⁶ 1n | GND | R⁸ D⁷ | SS¹⁴ flyback across fan 1 | C13 10u 50V | C14 10u 50V GND

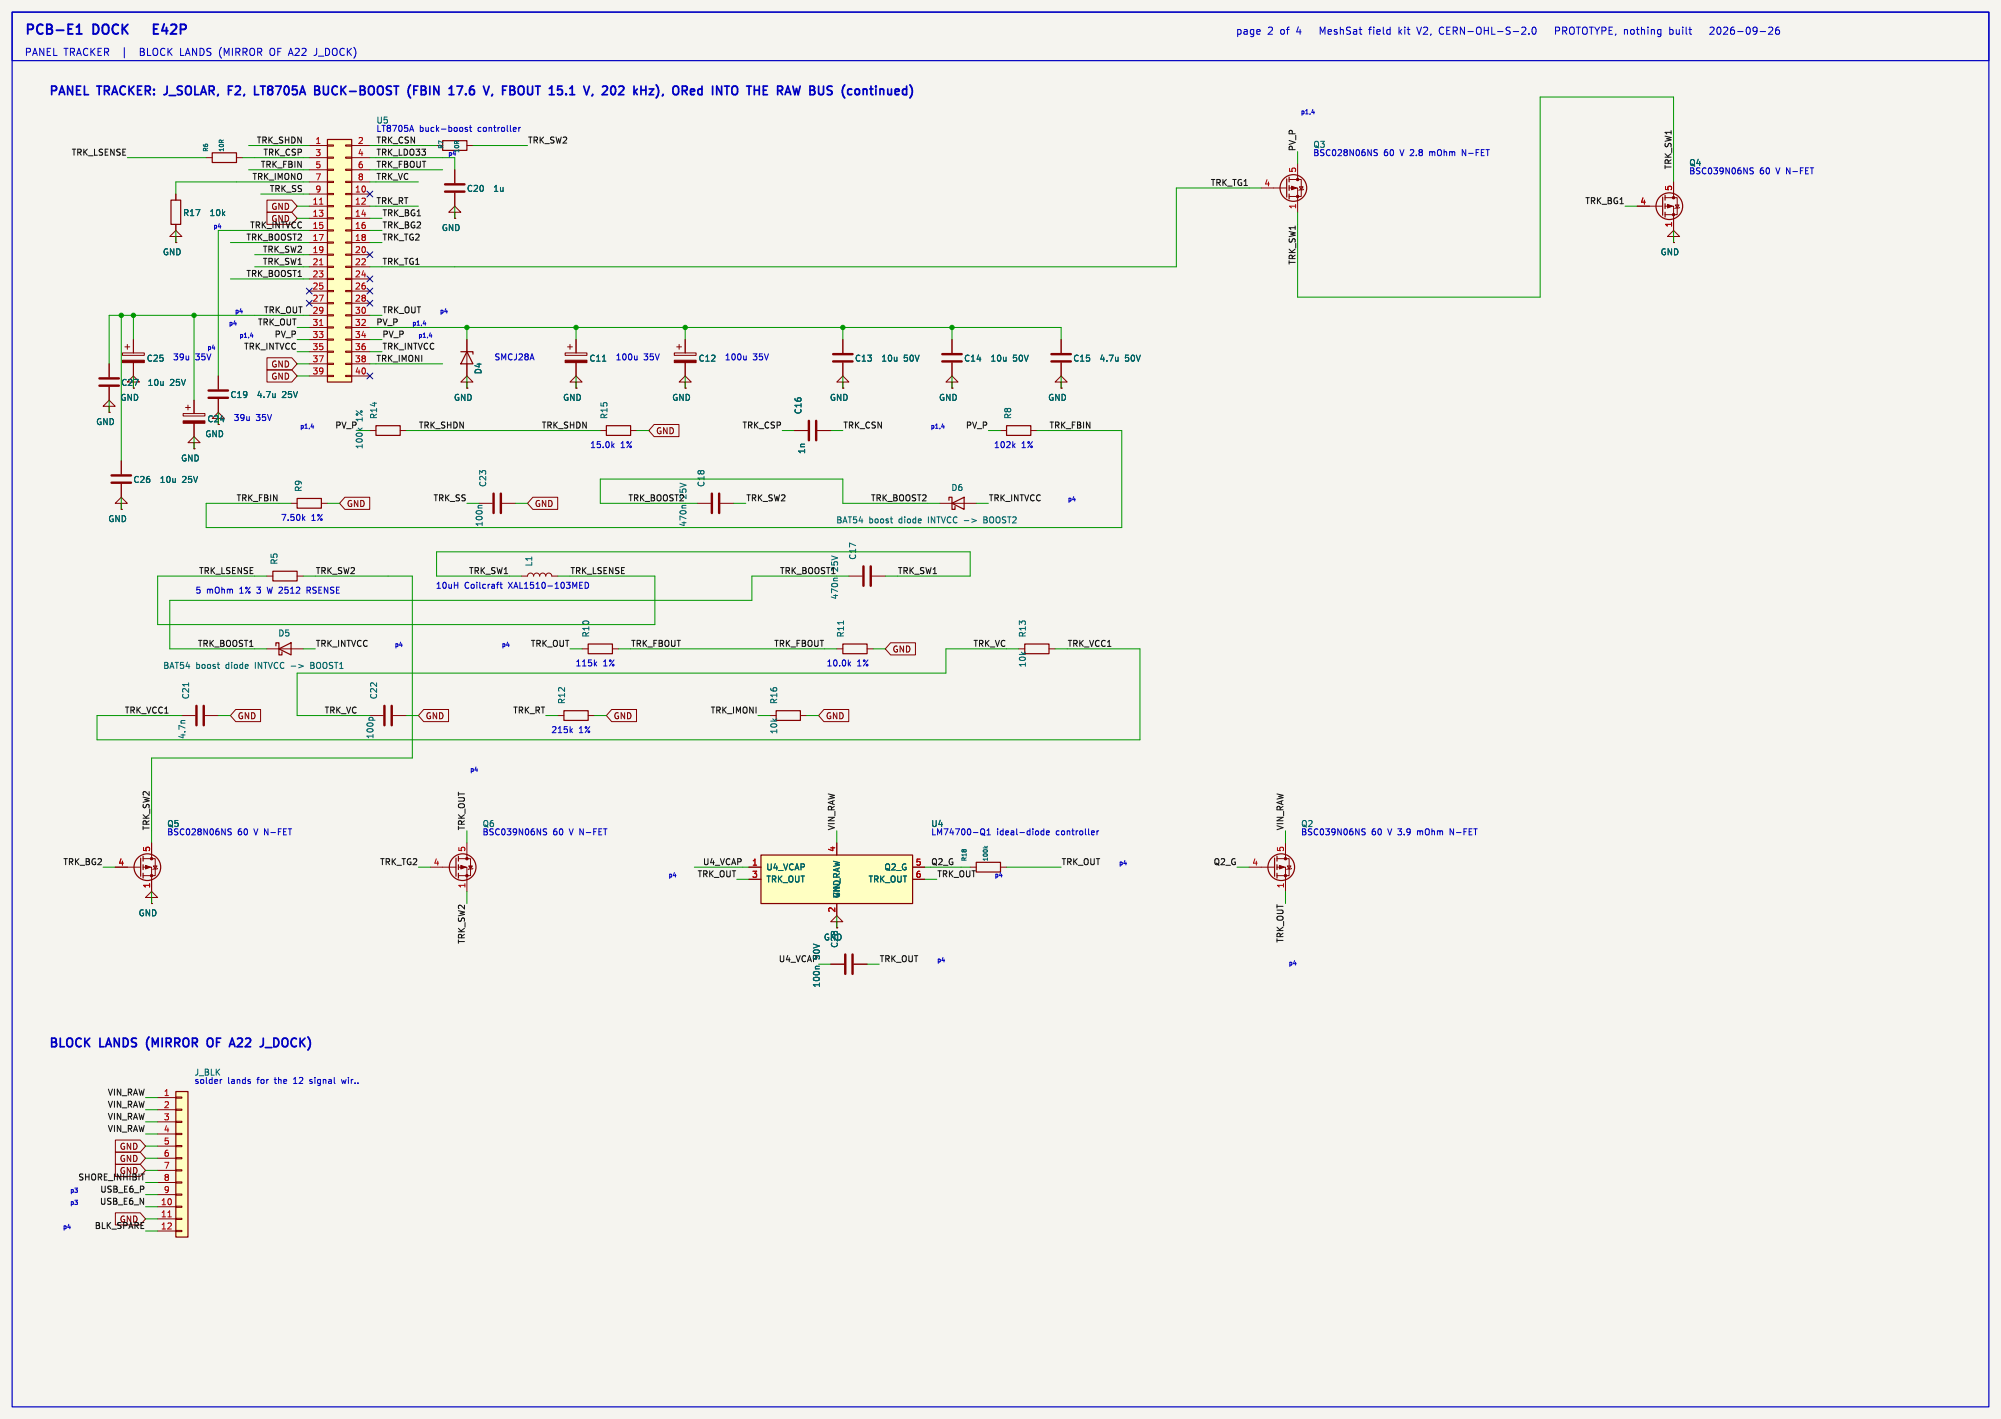
[picture p286: page 2]

PANEL TRACKER: J_SOLAR, F2, LT8705A BUCK-BOOST (FBIN 17.6 V, FBOUT 15.1 V, 202 kHz), ORed INTO THE RAW BUS (continued)

solder lands for the 12 signal wir.. BLOCK LANDS (MIRROR OF A22 J_DOCK)

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

# 100n R²⁷ 2.2k

LED1 C⁴⁶ 100n | GND | C⁵⁹ 100n

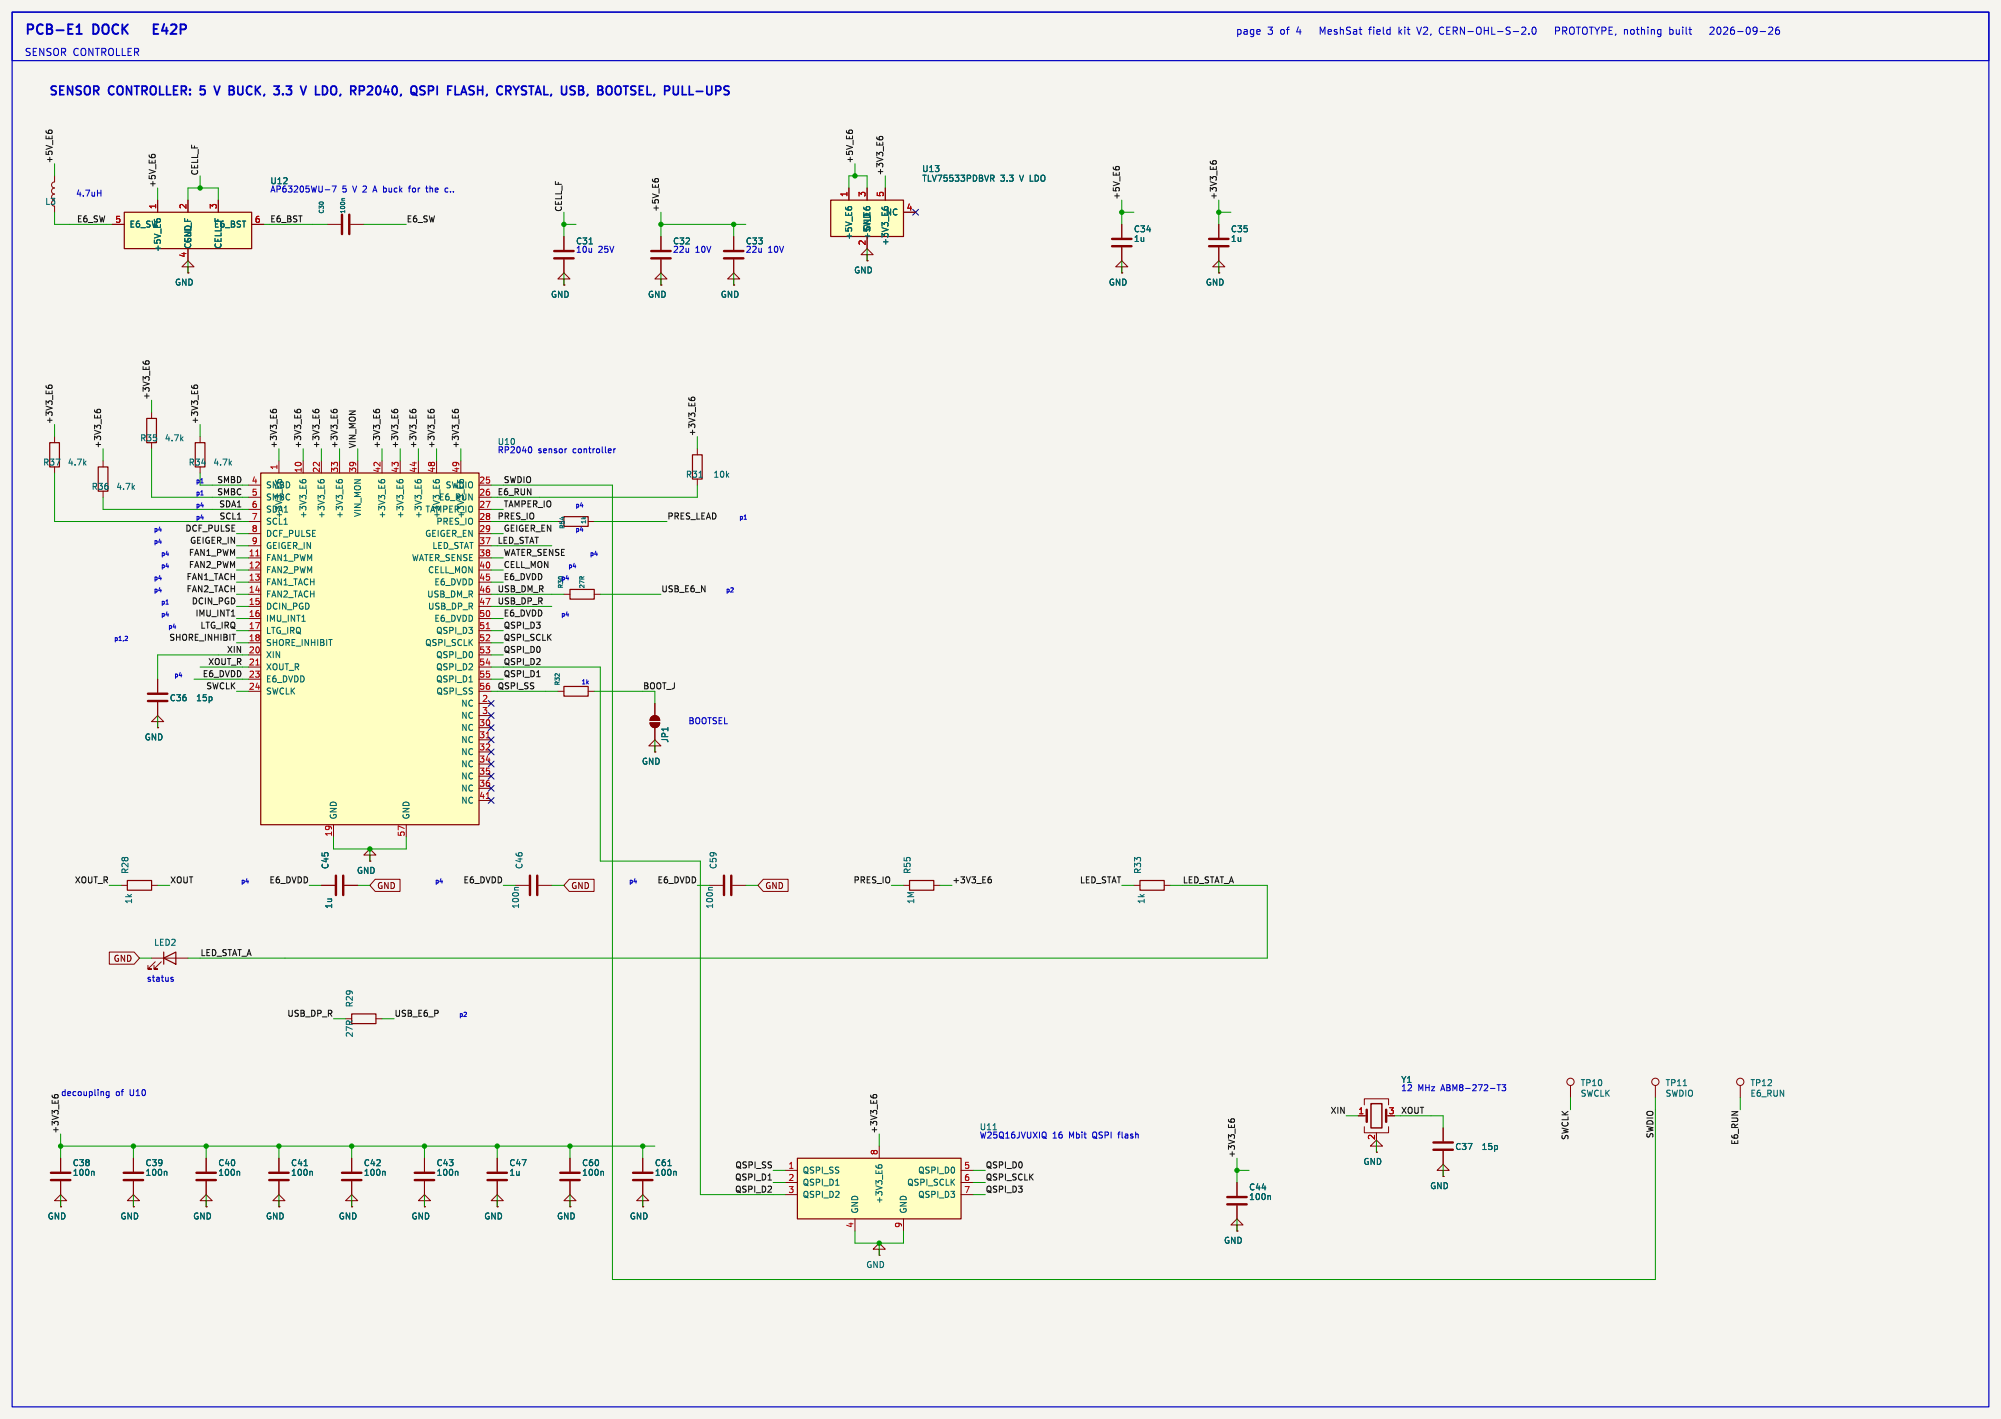
[picture p287: page 3]
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

LED_STAT 37 WATER_SENSE 38 CELL_MON 40 E6_DVDD 45 USB_DM_R 46 USB_DP_R 47 E6_DVDD 50 QSPI_D3 51 QSPI_SCLK 52 QSPI_D0 53 QSPI_D2 54 QSPI_D1 55 QSPI_SS 56 NC 2 NC 3 NC 30 NC 31 NC 32 NC 34 NC 35 NC 36 NC 41 U10
SMBD 4 SMBC 5 SDA1 6 SCL1 7 DCF_PULSE 8 GEIGER_IN 9 FAN1_PWM 11 FAN2_PWM 12 FAN1_TACH 13 FAN2_TACH 14 DCIN_PGD 15
SDA1

# J_FAN1 GND

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

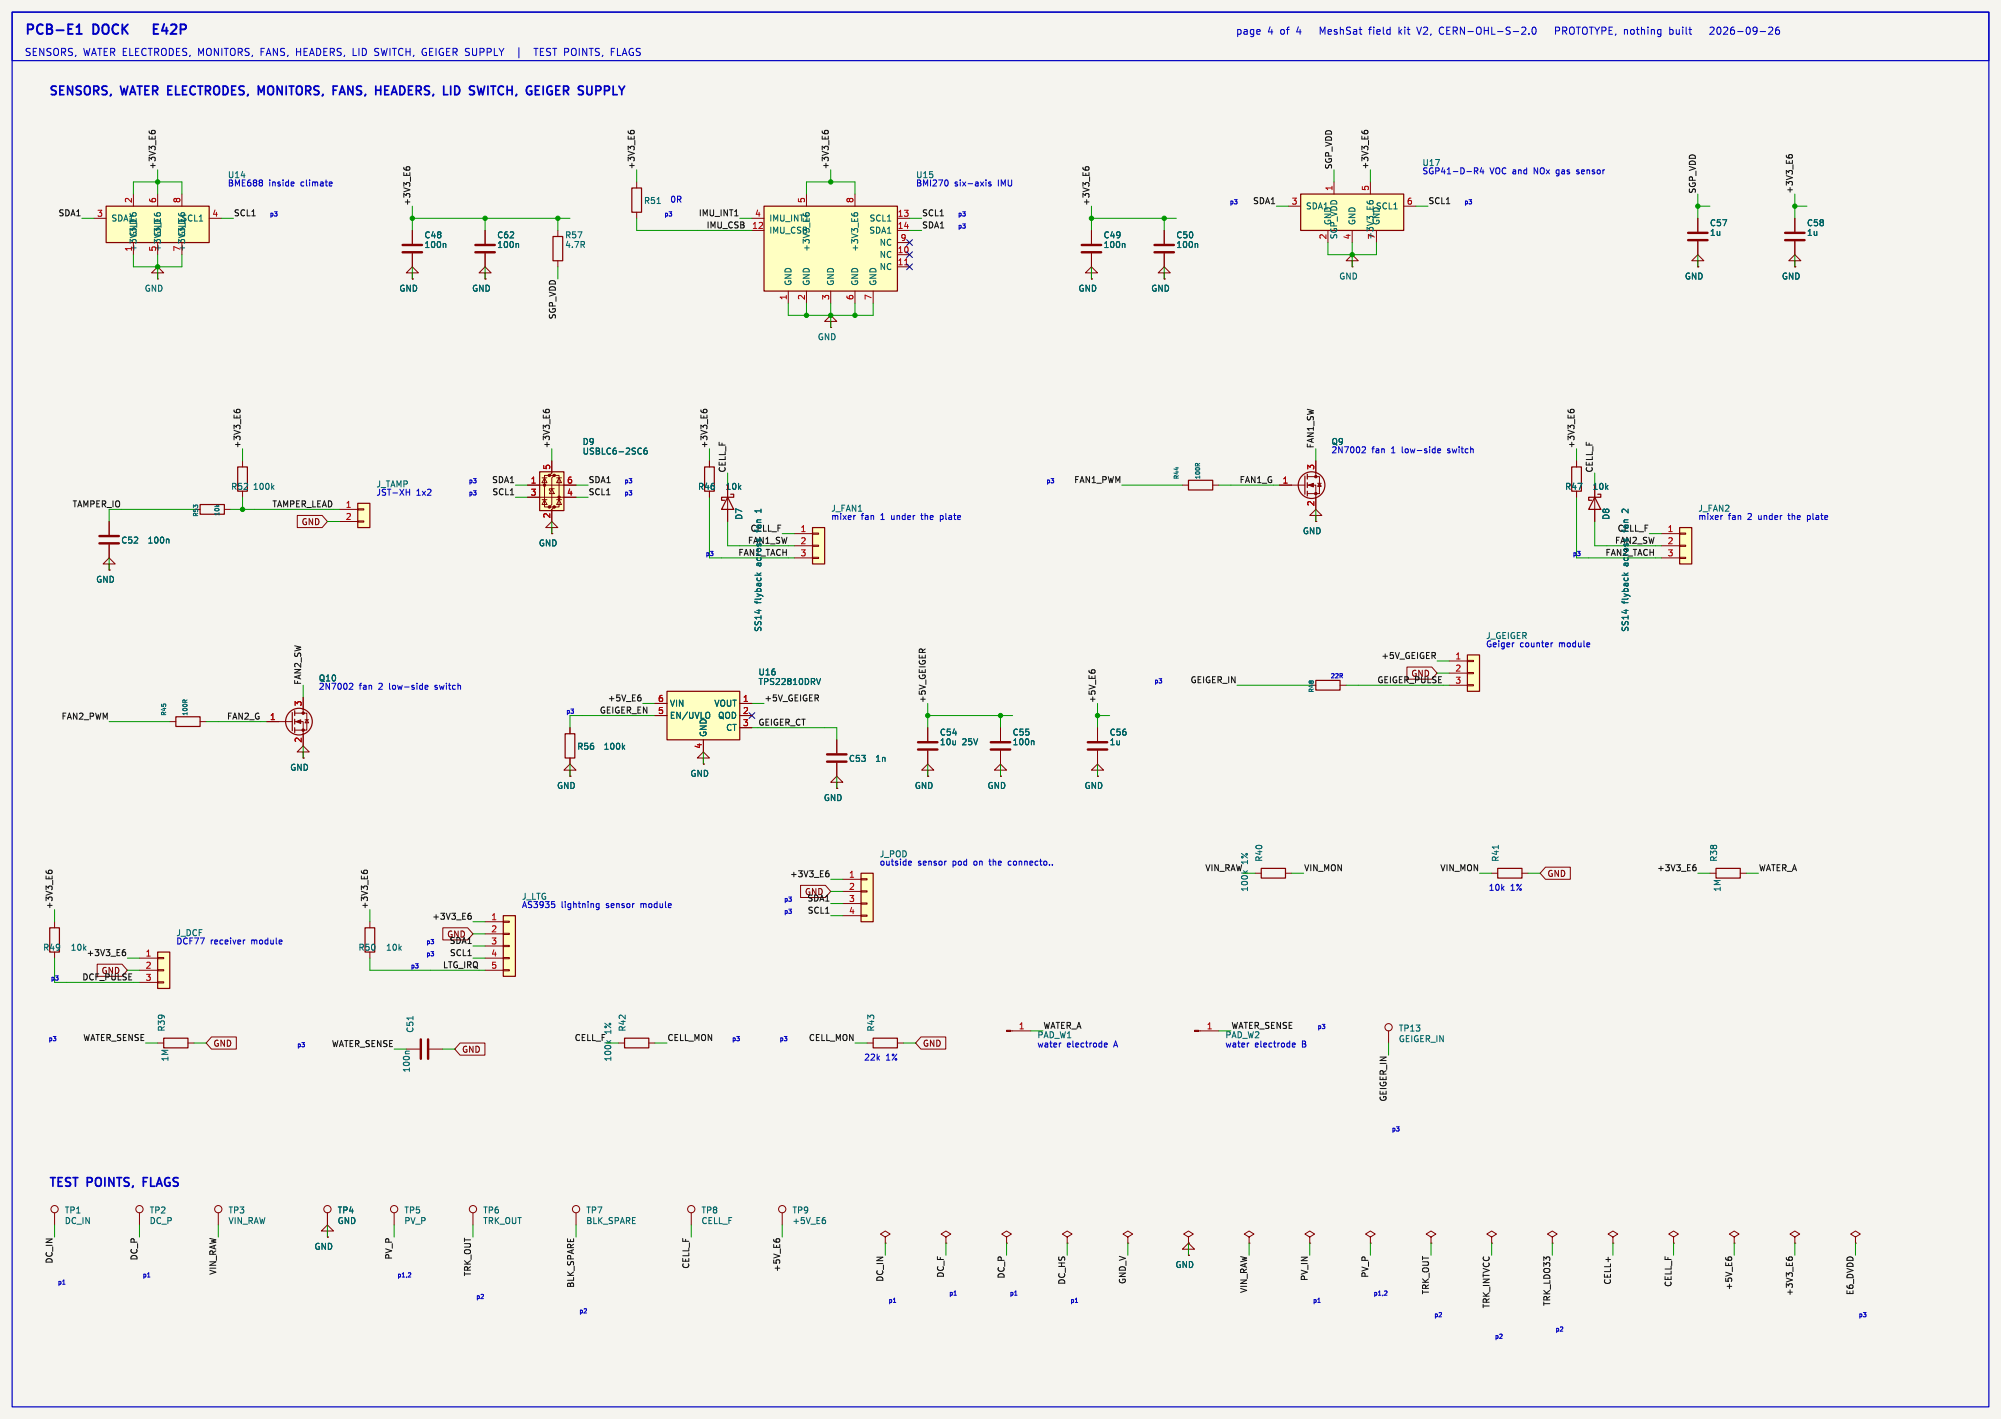
[picture p288: page 4]
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

SENSORS, WATER ELECTRODES, MONITORS, FANS, HEADERS, LID SWITCH, GEIGER SUPPLY

3 2 GND D7 SS14 flyback across fan 1 U16 TPS22810DRV

mixer fan 1 under the plate

J_POD
outside sensor pod on the connecto..
