meshsat/meshsat-fieldkit/v2/release/handover/H1/v2/docs/review-packets/battery/candidate/pcb-p-pack-schematic.pdf

# PBI 1 VC3 3 VC1 5 NC 7 VSS 9 TS2 11 TS4 13 BTP_INT 15 DISP 17 SMBC 19

LEDCNTLC 22 PTCEN 24 VCC 26 DSG 28 PCHG 30 BAT 32 U1 R¹⁸ | 5.1k | DSG_G 4 | PACK_P

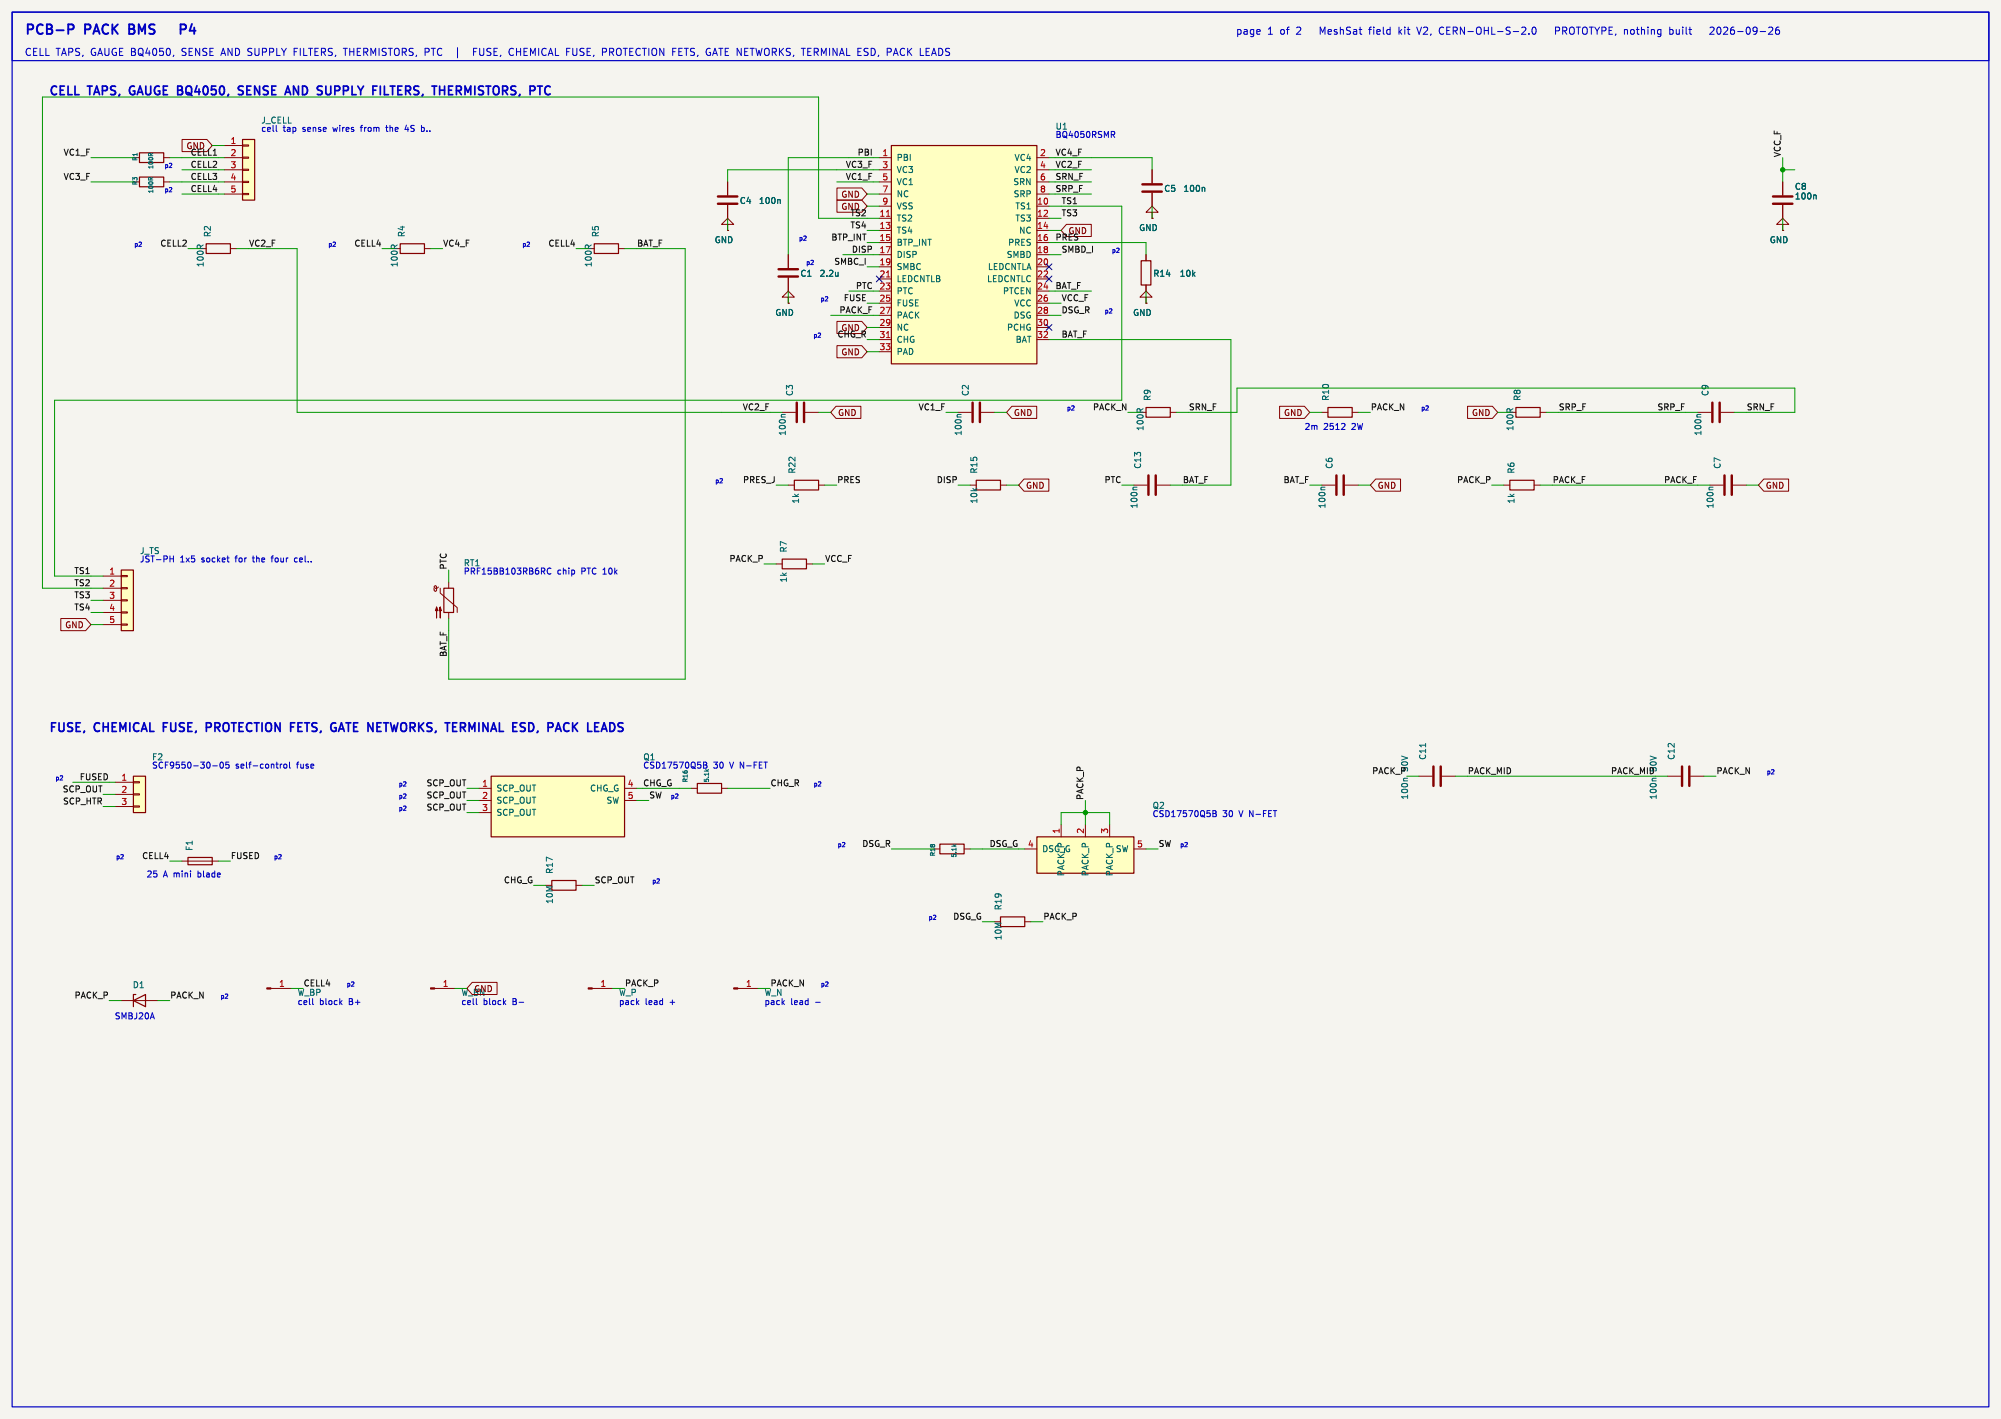
[picture p289: page 1]

CELL TAPS, GAUGE BQ4050, SENSE AND SUPPLY FILTERS, THERMISTORS, PTC

p2 FUSE, CHEMICAL FUSE, PROTECTION FETS, GATE NETWORKS, TERMINAL ESD, PACK LEADS

pack lead - p2 cell block B+

p1 PCB-P | PACK BMS | P4

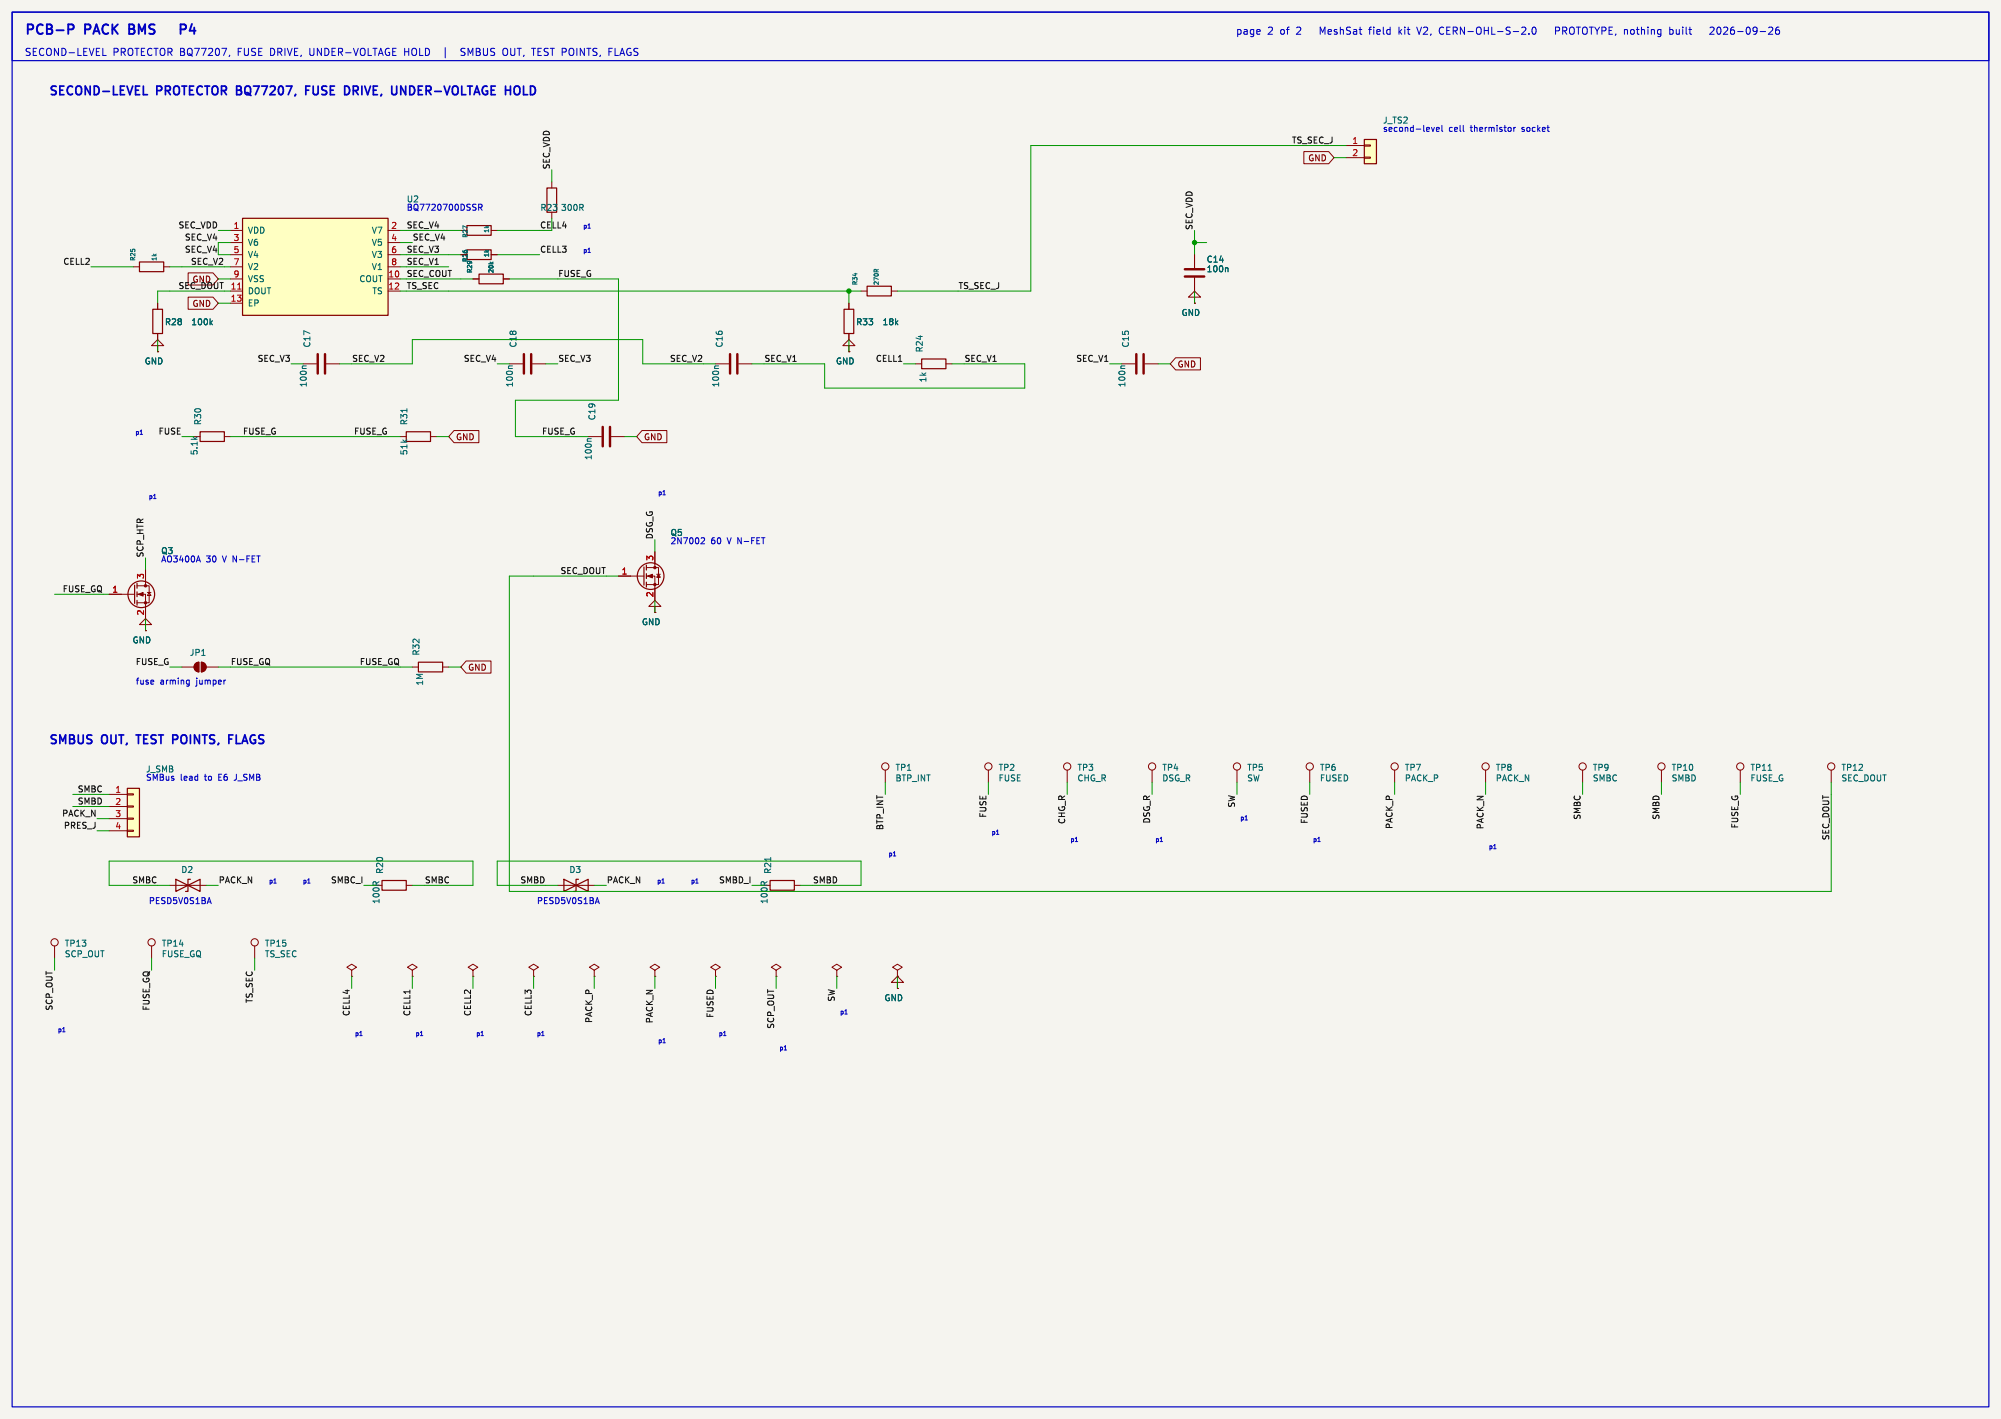
[picture p290: page 2]

p1 SMBUS OUT, TEST POINTS, FLAGS
