meshsat/meshsat-fieldkit/v2/docs/diagrams/pdf/arch-2-context.pdf

ARCHITECTURE.md, 2. Purpose and the prototype 1 core (lines 164 to 174 of the document with sha256/16 c883f948f3221e74): design diagram of an unbuilt prototype

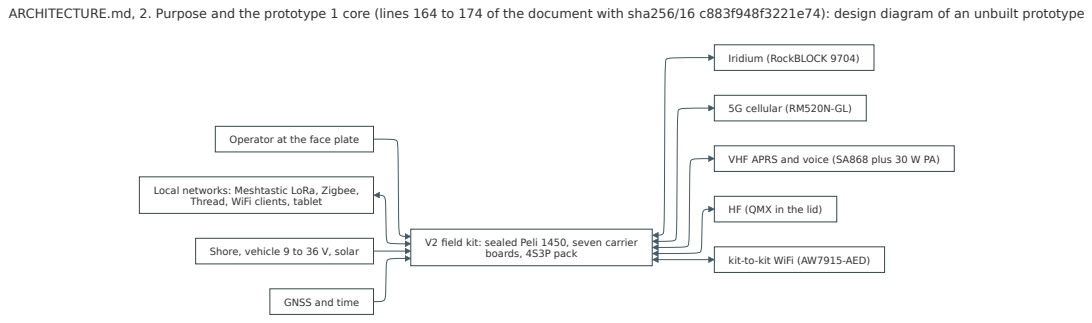
[picture p291: page 1]
boards, 4S3P pack; Iridium (RockBLOCK 9704); 5G cellular (RM520N-GL)

Operator at the face plate

VHF APRS and voice (SA868 plus 30 W PA)

Local networks: Meshtastic LoRa, Zigbee,

Thread, WiFi clients, tablet

HF (QMX in the lid)

V2 field kit: sealed Peli 1450, seven carrier

Shore, vehicle 9 to 36 V, solar

kit-to-kit WiFi (AW7915-AED)

GNSS and time
