meshsat/meshsat-fieldkit/v2/docs/diagrams/pdf/arch-3-2-board-interconnect.pdf

ARCHITECTURE.md, 3.2 Inputs, outputs and failure boundaries (lines 254 to 268 of the document with sha256/16 c883f948f3221e74): design diagram of an unbuilt prototype

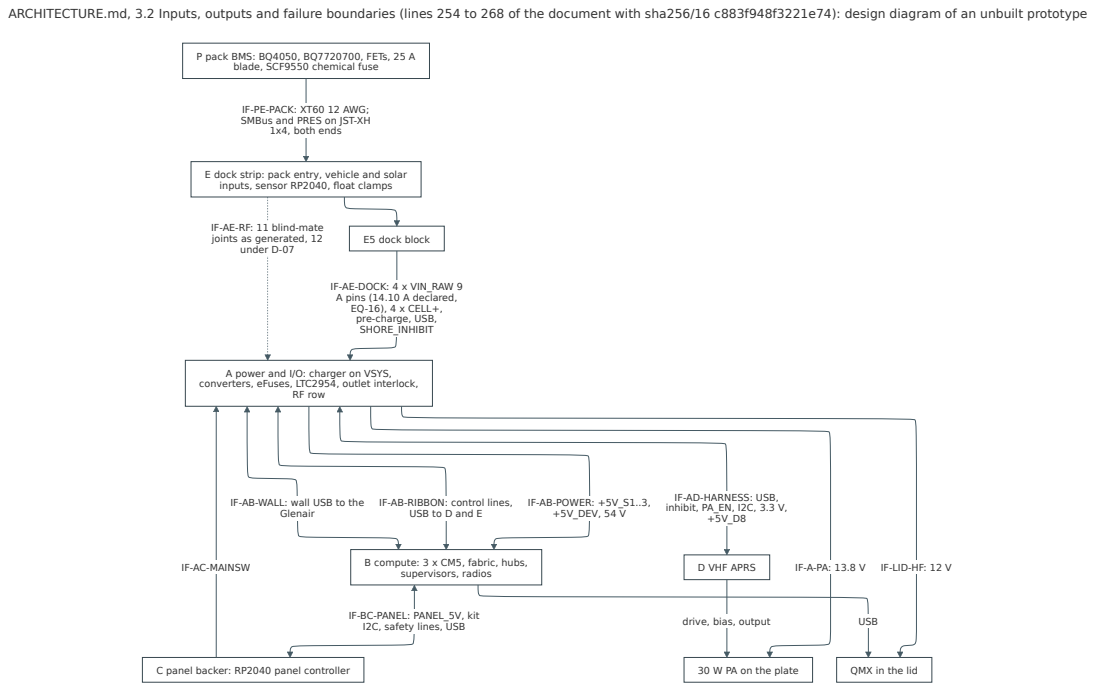
[picture p292: page 1]
E5 dock block; RF row; supervisors, radios; D VHF APRS; C panel backer: RP2040 panel controller; 30 W PA on the plate; QMX in the lid; Glenair; IF-AC-MAINSW; USB

P pack BMS: BQ4050, BQ7720700, FETs, 25 A

blade, SCF9550 chemical fuse

IF-PE-PACK: XT60 12 AWG;
SMBus and PRES on JST-XH
1x4, both ends

E dock strip: pack entry, vehicle and solar
inputs, sensor RP2040, float clamps

IF-AE-RF: 11 blind-mate
joints as generated, 12
under D-07

IF-AE-DOCK: 4 x VIN_RAW 9
A pins (14.10 A declared,
EQ-16), 4 x CELL+,
pre-charge, USB,
SHORE_INHIBIT

A power and I/O: charger on VSYS,
converters, eFuses, LTC2954, outlet interlock,

IF-AB-WALL: wall USB to the

IF-AB-RIBBON: control lines,
USB to D and E

IF-AB-POWER: +5V_S1..3,
+5V_DEV, 54 V

IF-AD-HARNESS: USB,
inhibit, PA_EN, I2C, 3.3 V,

B compute: 3 x CM5, fabric, hubs,

IF-LID-HF: 12 V

IF-BC-PANEL: PANEL_5V, kit
I2C, safety lines, USB

drive, bias, output
