meshsat/meshsat-fieldkit/v2/docs/diagrams/pdf/arch-4-1-power-tree.pdf

ARCHITECTURE.md, 4.1 The power tree as generated (lines 281 to 313 of the document with sha256/16 c883f948f3221e74): design diagram of an unbuilt prototype

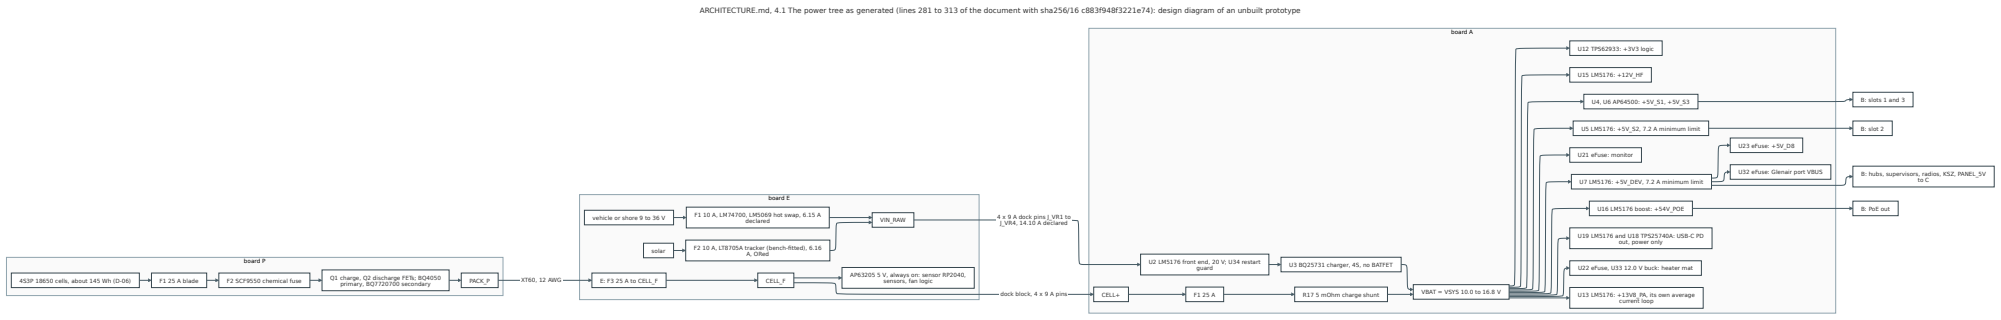
[picture p293: page 1]

U32 eFuse: Glenair port VBUS

B: hubs, supervisors, radios, KSZ, PANEL_5V

vehicle or shore 9 to 36 V

U22 eFuse, U33 12.0 V buck: heater mat
