meshsat/meshsat-fieldkit/v2/docs/diagrams/pdf/arch-5-5-lanes-and-fabric.pdf

ARCHITECTURE.md, 5.5 Ethernet, display, the kit I2C bus and the supervisor fabric (lines 626 to 654 of the document with sha256/16 c883f948f3221e74): design diagram of an unbuilt prototype

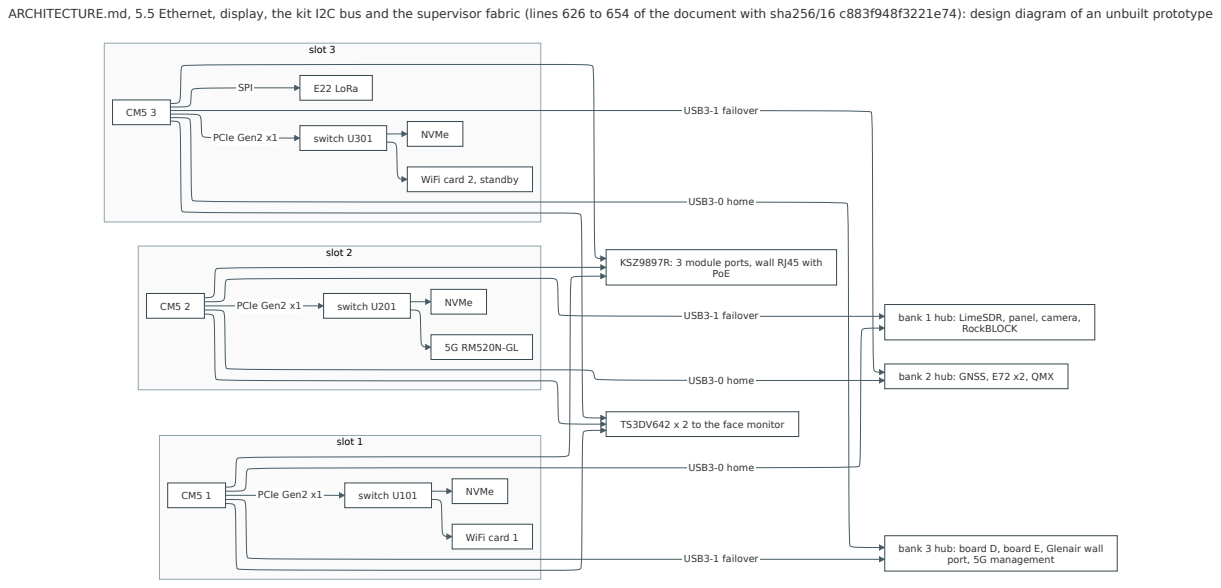
[picture p294: page 1]
slot 3; slot 2; slot 1; switch U301; NVMe; E22 LoRa; switch U201; switch U101; WiFi card 1; RockBLOCK; port, 5G management; PoE; PCIe Gen2 x1; SPI; USB3-0 home; USB3-1 failover

WiFi card 2, standby

KSZ9897R: 3 module ports, wall RJ45 with

bank 1 hub: LimeSDR, panel, camera,

bank 2 hub: GNSS, E72 x2, QMX

TS3DV642 x 2 to the face monitor

bank 3 hub: board D, board E, Glenair wall
