meshsat/meshsat-fieldkit/v2/docs/diagrams/pdf/battery-charger-states.pdf

review-packets/battery/CHARGER-STATE-SEQUENCE.md, 7. Items this produces (owners named; none written by this stream) (lines 170 to 184 of the document with sha256/16 44fdf9a022c49337): design diagram of an unbuilt prototype

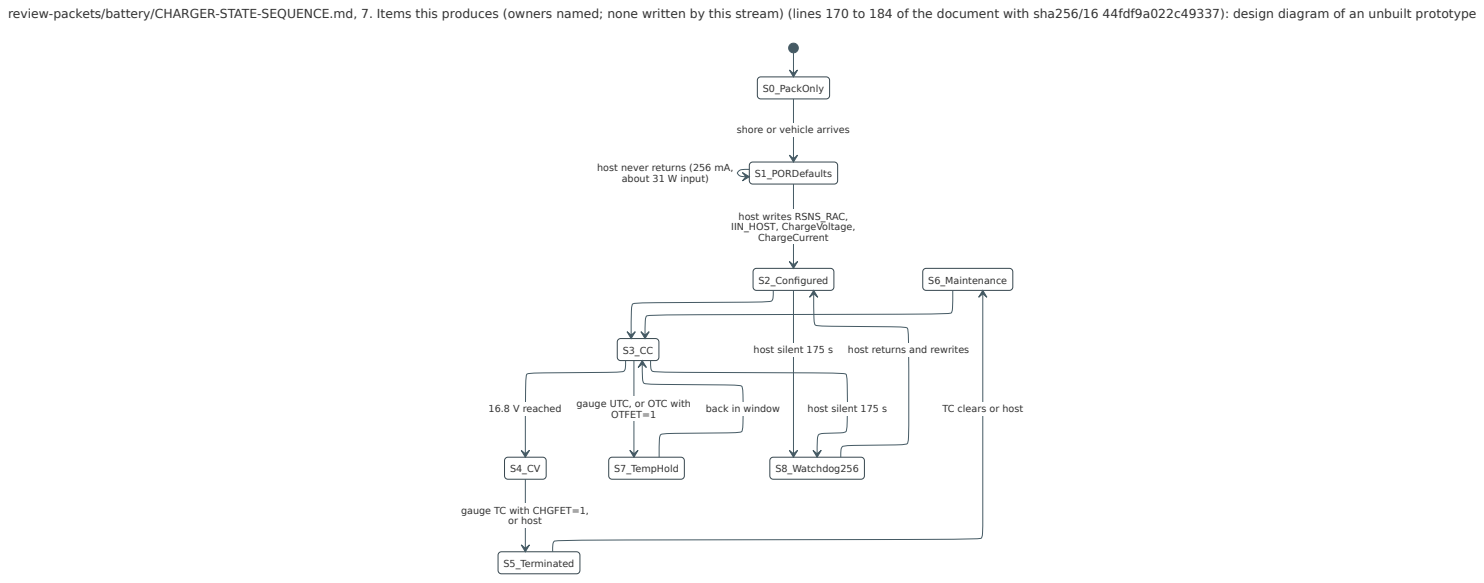
[picture p295: page 1]
S0_PackOnly; S1_PORDefaults; S2_Configured; S5_Terminated; S6_Maintenance; S7_TempHold; S8_Watchdog256; host writes RSNS_RAC, IIN_HOST, ChargeVoltage, ChargeCurrent; 16.8 V reached; or host; OTFET=1; back in window; host silent 175 s

shore or vehicle arrives

host never returns (256 mA,
about 31 W input)

host returns and rewrites

TC clears or host gauge UTC, or OTC with

gauge TC with CHGFET=1,
