meshsat/meshsat-fieldkit/v2/docs/diagrams/pdf/battery-protection-states.pdf

review-packets/battery/PROTECTION-ARCHITECTURE.md, 4. States (lines 99 to 112 of the document with sha256/16 c1fa24d2ee645a1d): design diagram of an unbuilt prototype

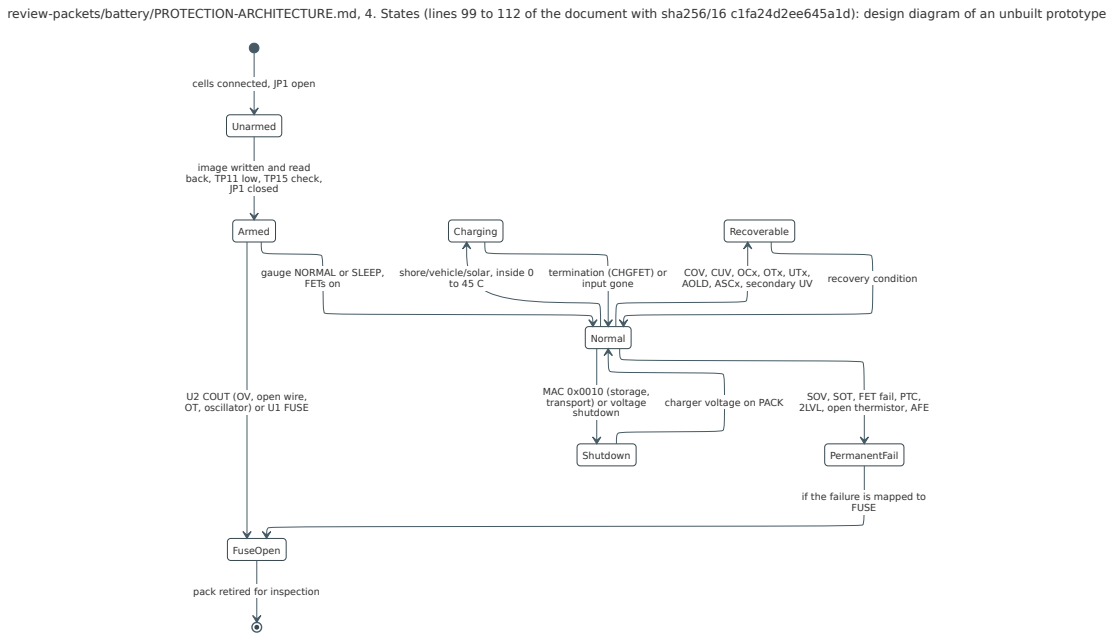
[picture p296: page 1]
Unarmed; Armed; Normal; Charging; Recoverable; Shutdown; PermanentFail; FuseOpen; JP1 closed; FETs on; input gone; recovery condition; FUSE

cells connected, JP1 open

image written and read
back, TP11 low, TP15 check,

gauge NORMAL or SLEEP,

shore/vehicle/solar, inside 0

termination (CHGFET) or

COV, CUV, OCx, OTx, UTx,
AOLD, ASCx, secondary UV

MAC 0x0010 (storage,
transport) or voltage
shutdown

U2 COUT (OV, open wire,
OT, oscillator) or U1 FUSE

SOV, SOT, FET fail, PTC,
2LVL, open thermistor, AFE

charger voltage on PACK

if the failure is mapped to

pack retired for inspection
