meshsat/meshsat-fieldkit/v2/docs/diagrams/pdf/control-lines.pdf

Control lines across the boards, read from the netlists named in each board's box (design diagram of an unbuilt prototype)

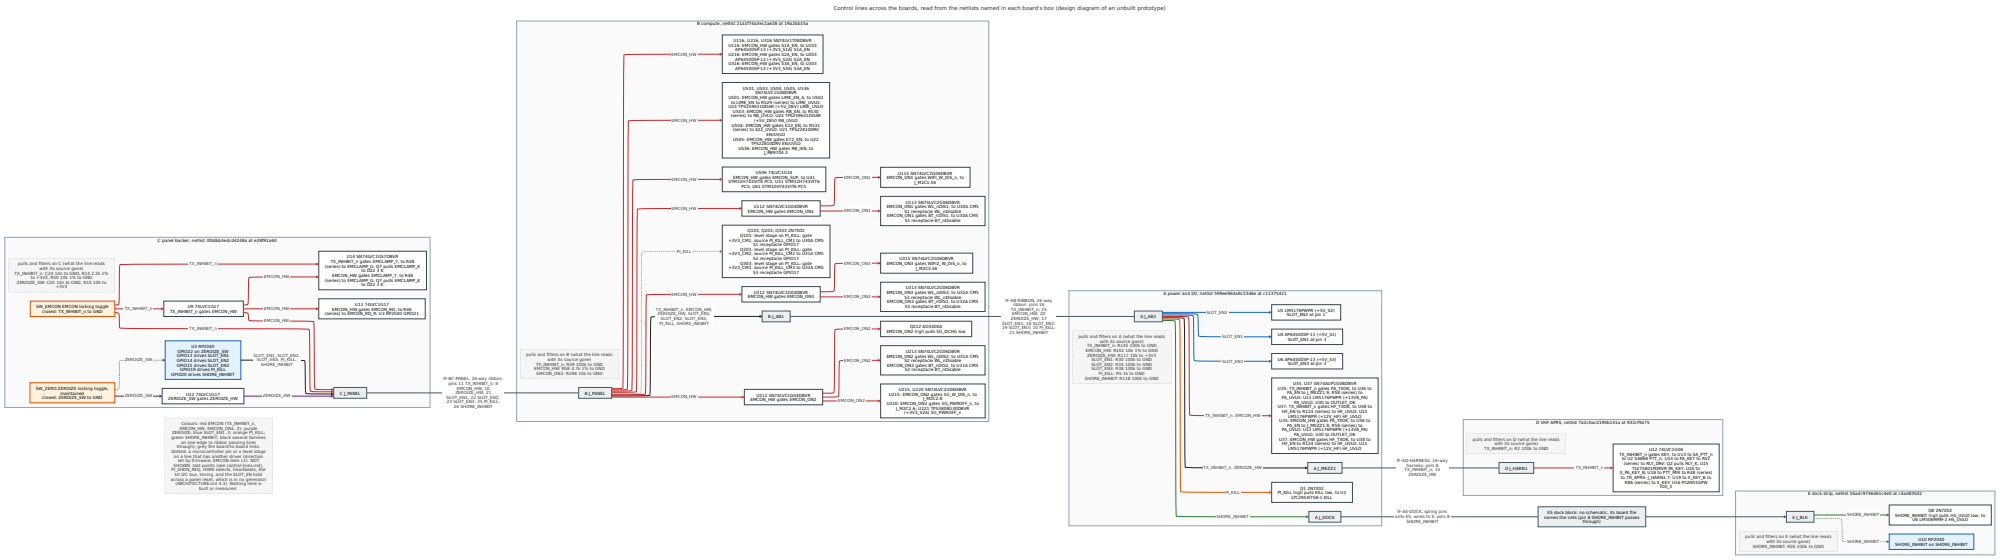
[picture p297: page 1]

U501: EMCON_HW gates LIME_EN_A, to U502
to LIME_EN to R529 (series) to LIME_UVLO:
U23 TPS259631DDAR (+5V_DEV) LIME_UVLO
U503: EMCON_HW gates RB_EN, to R530
(series) to RB_UVLO: U24 TPS259631DDAR

Q103: level stage on PI_KILL: gate
+3V3_CM1, source PI_KILL_CM1 to U30A CM5

C panel backer, netlist 3fddbb3edcd4248a at e28f91a60

S1 receptacle GPIO17
Q203: level stage on PI_KILL: gate
+3V3_CM2, source PI_KILL_CM2 to U31A CM5

S2 receptacle GPIO17
Q303: level stage on PI_KILL: gate
+3V3_CM3, source PI_KILL_CM3 to U32A CM5

pulls and filters on C (what the line reads

with its source gone)

A power and I/O, netlist 599ee964a9c23d6e at c11375421

pulls and filters on A (what the line reads

TX_INHIBIT_n: R145 100k to GND
EMCON_HW: R102 10k 1% to GND
ZEROIZE_HW: R117 10k to +3V3
SLOT_EN1: R30 100k to GND
SLOT_EN2: R34 100k to GND
SLOT_EN3: R38 100k to GND
PI_KILL: R5 1k to GND
SHORE_INHIBIT: R118 100k to GND

pulls and filters on B (what the line reads

TX_INHIBIT_n: R59 100k to GND
EMCON_HW: R58 4.7k 1% to GND
EMCON_ON2: R296 10k to GND

D VHF APRS, netlist 7a2c0ac2190b141a at 932cf9d75

Colours: red EMCON (TX_INHIBIT_n,
EMCON_HW, EMCON_ON1..3); purple
ZEROIZE; blue SLOT_EN1..3; orange PI_KILL;
green SHORE_INHIBIT; black several families
on one edge (a ribbon passing lines
through); grey the board-to-board links.
Dotted: a microcontroller pin or a level stage
on a line that has another driver (direction
set by firmware, EMCON item L1). NOT
SHOWN: test points (see control-lines.md),
PI_SHDN_REQ, HDMI selects, heartbeats, the
kit I2C bus, timing, and the SLOT_EN hold
across a panel reset, which is in no generator
(ARCHITECTURE.md 4.3). Nothing here is

pulls and filters on D (what the line reads

TX_INHIBIT_n: R2 100k to GND

TX_INHIBIT_n gates KEY, to U13 to SA_PTT_n
to U2 SA868 PTT_n; U14 to PA_KEY to R52
(series) to RLY_DRV: Q2 pulls RLY_K, U15
TLV75801PDRVR PA_KEY, U20 to
X_PA_KEY_B; U18 to PTT_MIR to R48 (series)
to TR_APRS: J_HARN1.7; U19 to X_KEY_B to
R86 (series) to X_KEY: U16 PCA9555PW

PI_KILL high pulls KILL low, to U1
LTC2954ITS8-1 KILL

E dock strip, netlist 56adc9746d61c4e0 at c4ad83502

IF-AE-DOCK, spring pins
onto E5, wires to E: pins 8
SHORE_INHIBIT

E5 dock block: no schematic, its board file
names the nets (pin 8 SHORE_INHIBIT passes

SHORE_INHIBIT high pulls HS_UVLO low, to

pulls and filters on E (what the line reads

SHORE_INHIBIT: R26 100k to GND
