meshsat/meshsat-fieldkit/v2/release/revA/review/PCB-C-DISPLAY-C7/pcb-c-display-assembly-top.pdf

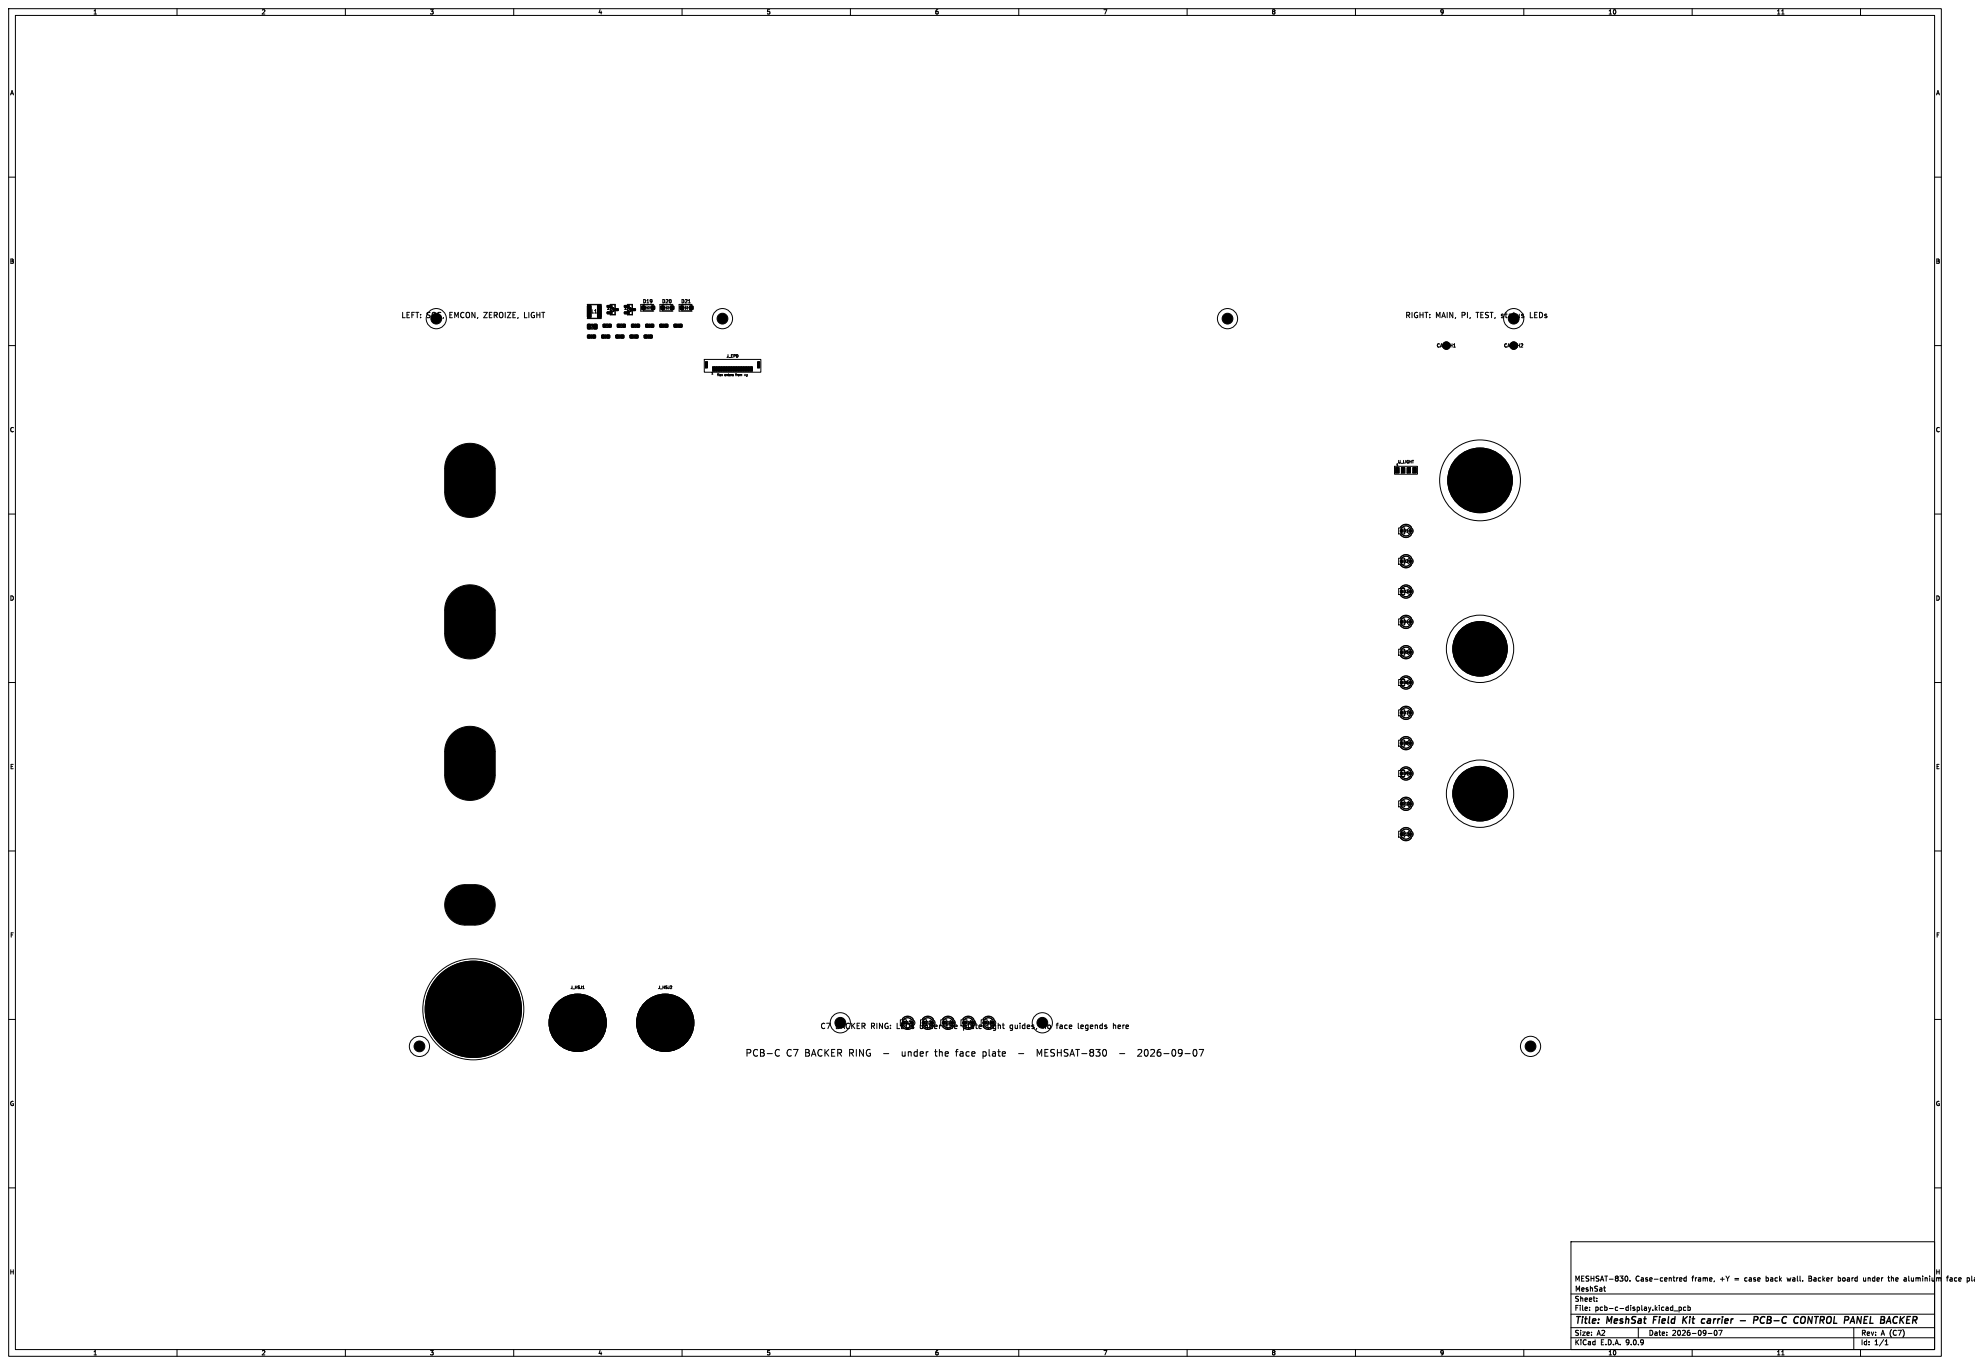
[picture p298: page 1]
