meshsat/meshsat-fieldkit/v2/release/revA/review/PCB-E1-DOCK-E6/pcb-e1-dock-assembly-bottom-mirrored.pdf

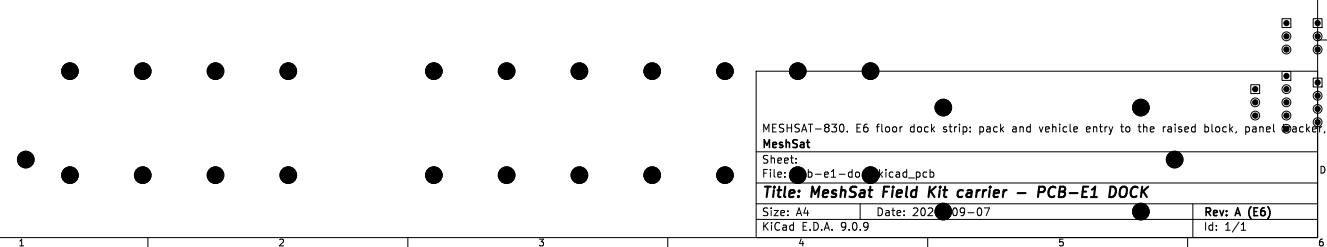
[picture p299: page 1]
