meshsat/meshsat-fieldkit/v2/release/revA/review/PCB-E1-DOCK-E6/pcb-e1-dock-assembly-top.pdf

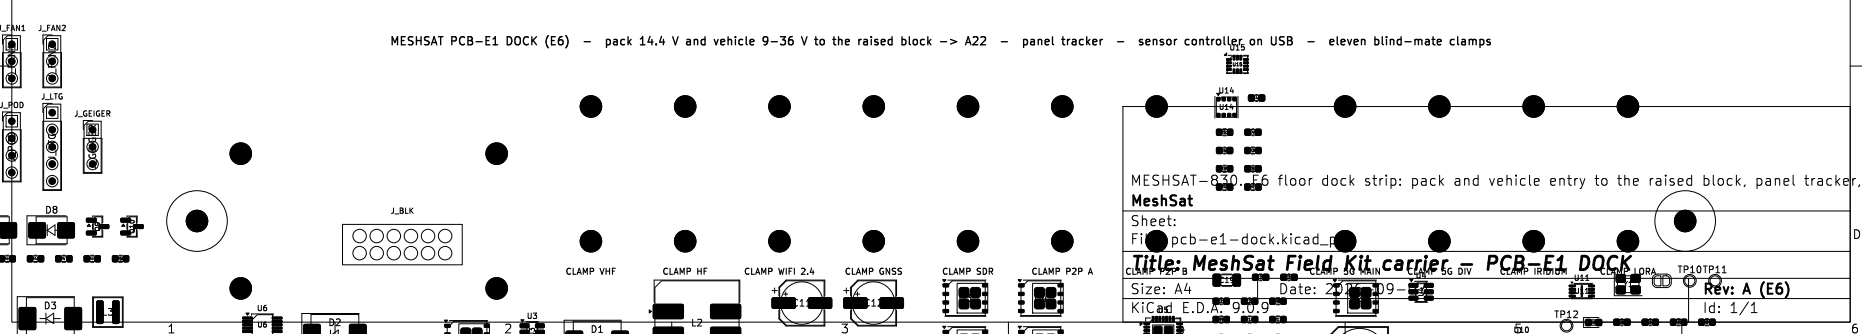
[picture p300: page 1]
