meshsat/meshsat-fieldkit/v2/release/revA/review/PCB-E5-BLOCK-E5/pcb-e5-block-assembly-bottom-mirrored.pdf

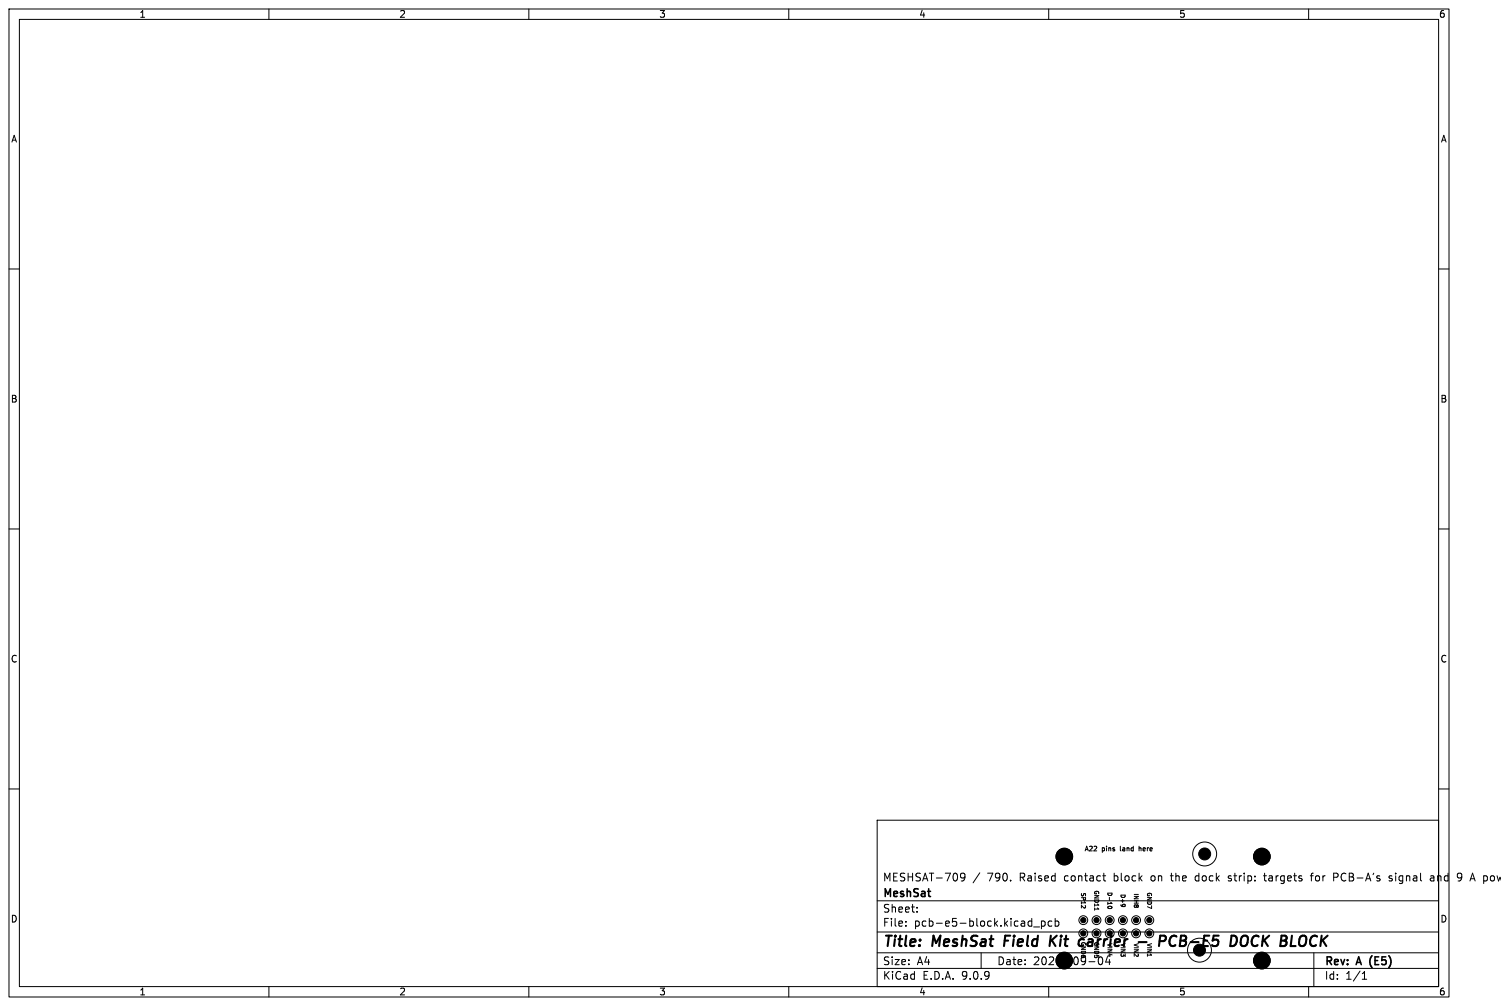
[picture p301: page 1]
