meshsat/meshsat-fieldkit/v2/release/revA/review/PCB-E5-BLOCK-E5/pcb-e5-block-assembly-top.pdf

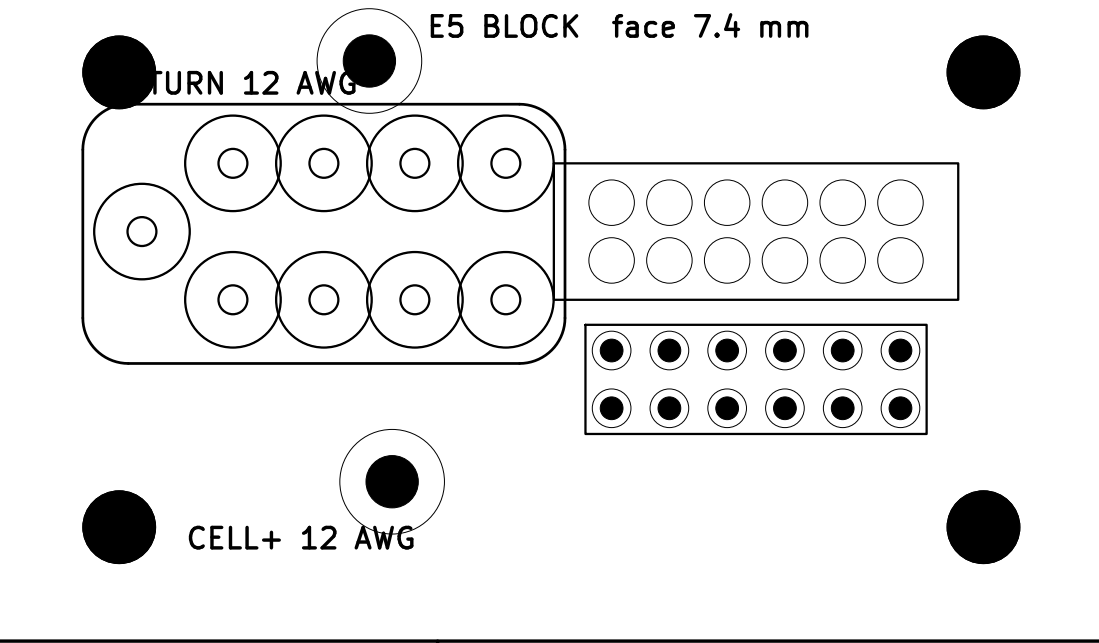
[picture p302: page 1]
