meshsat/meshsat-fieldkit/v2/release/revA/boards/meshsat-pcb-c-revA-C24/pcb-c-display-1to1-bottom-mirrored.pdf

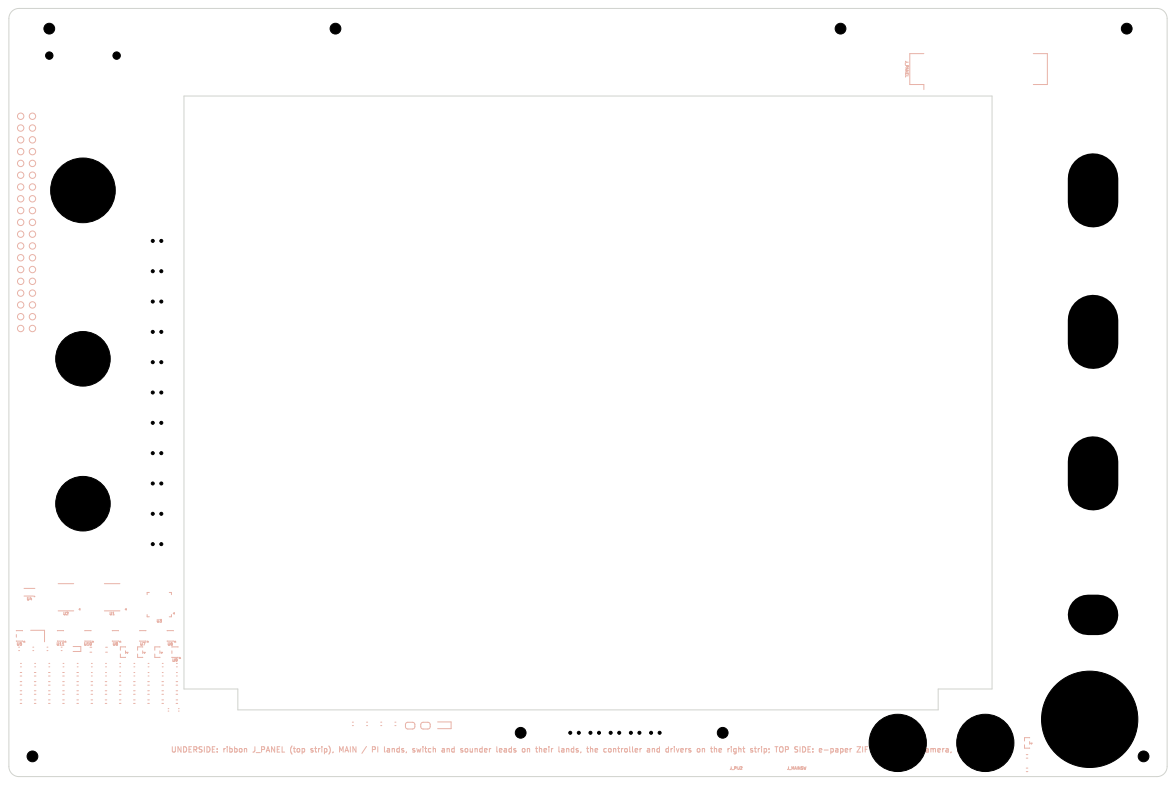
[picture p303: page 1]
