meshsat/meshsat-fieldkit/v2/release/revA/boards/meshsat-pcb-c-revA-C24/pcb-c-display-1to1-top.pdf

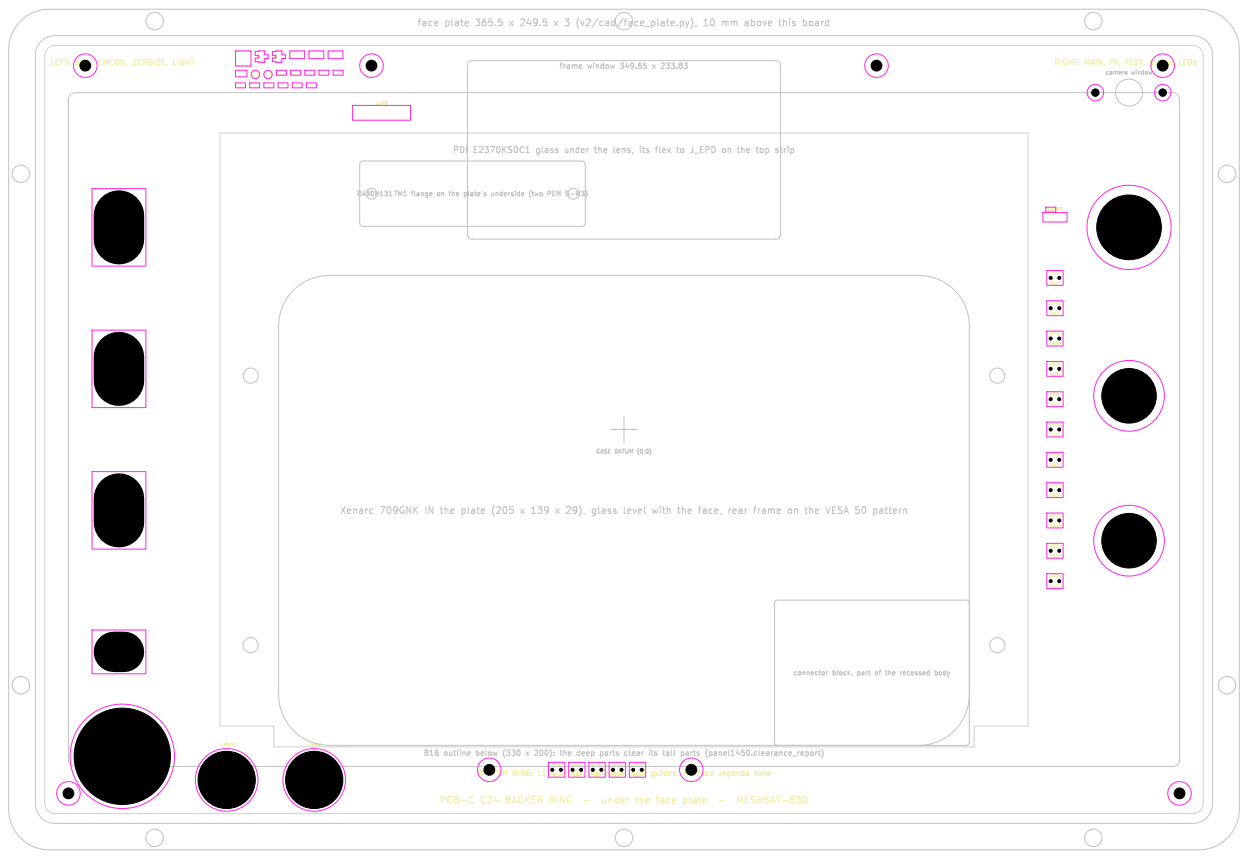
[picture p304: page 1]
