meshsat/meshsat-fieldkit/v2/release/revA/boards/meshsat-pcb-c-revA-C6/pcb-c-display.kicad_pcb

## KiCad design v2/release/revA/boards/meshsat-pcb-c-revA-C6/pcb-c-display.kicad_pcb (2026-09-06, an earlier design)

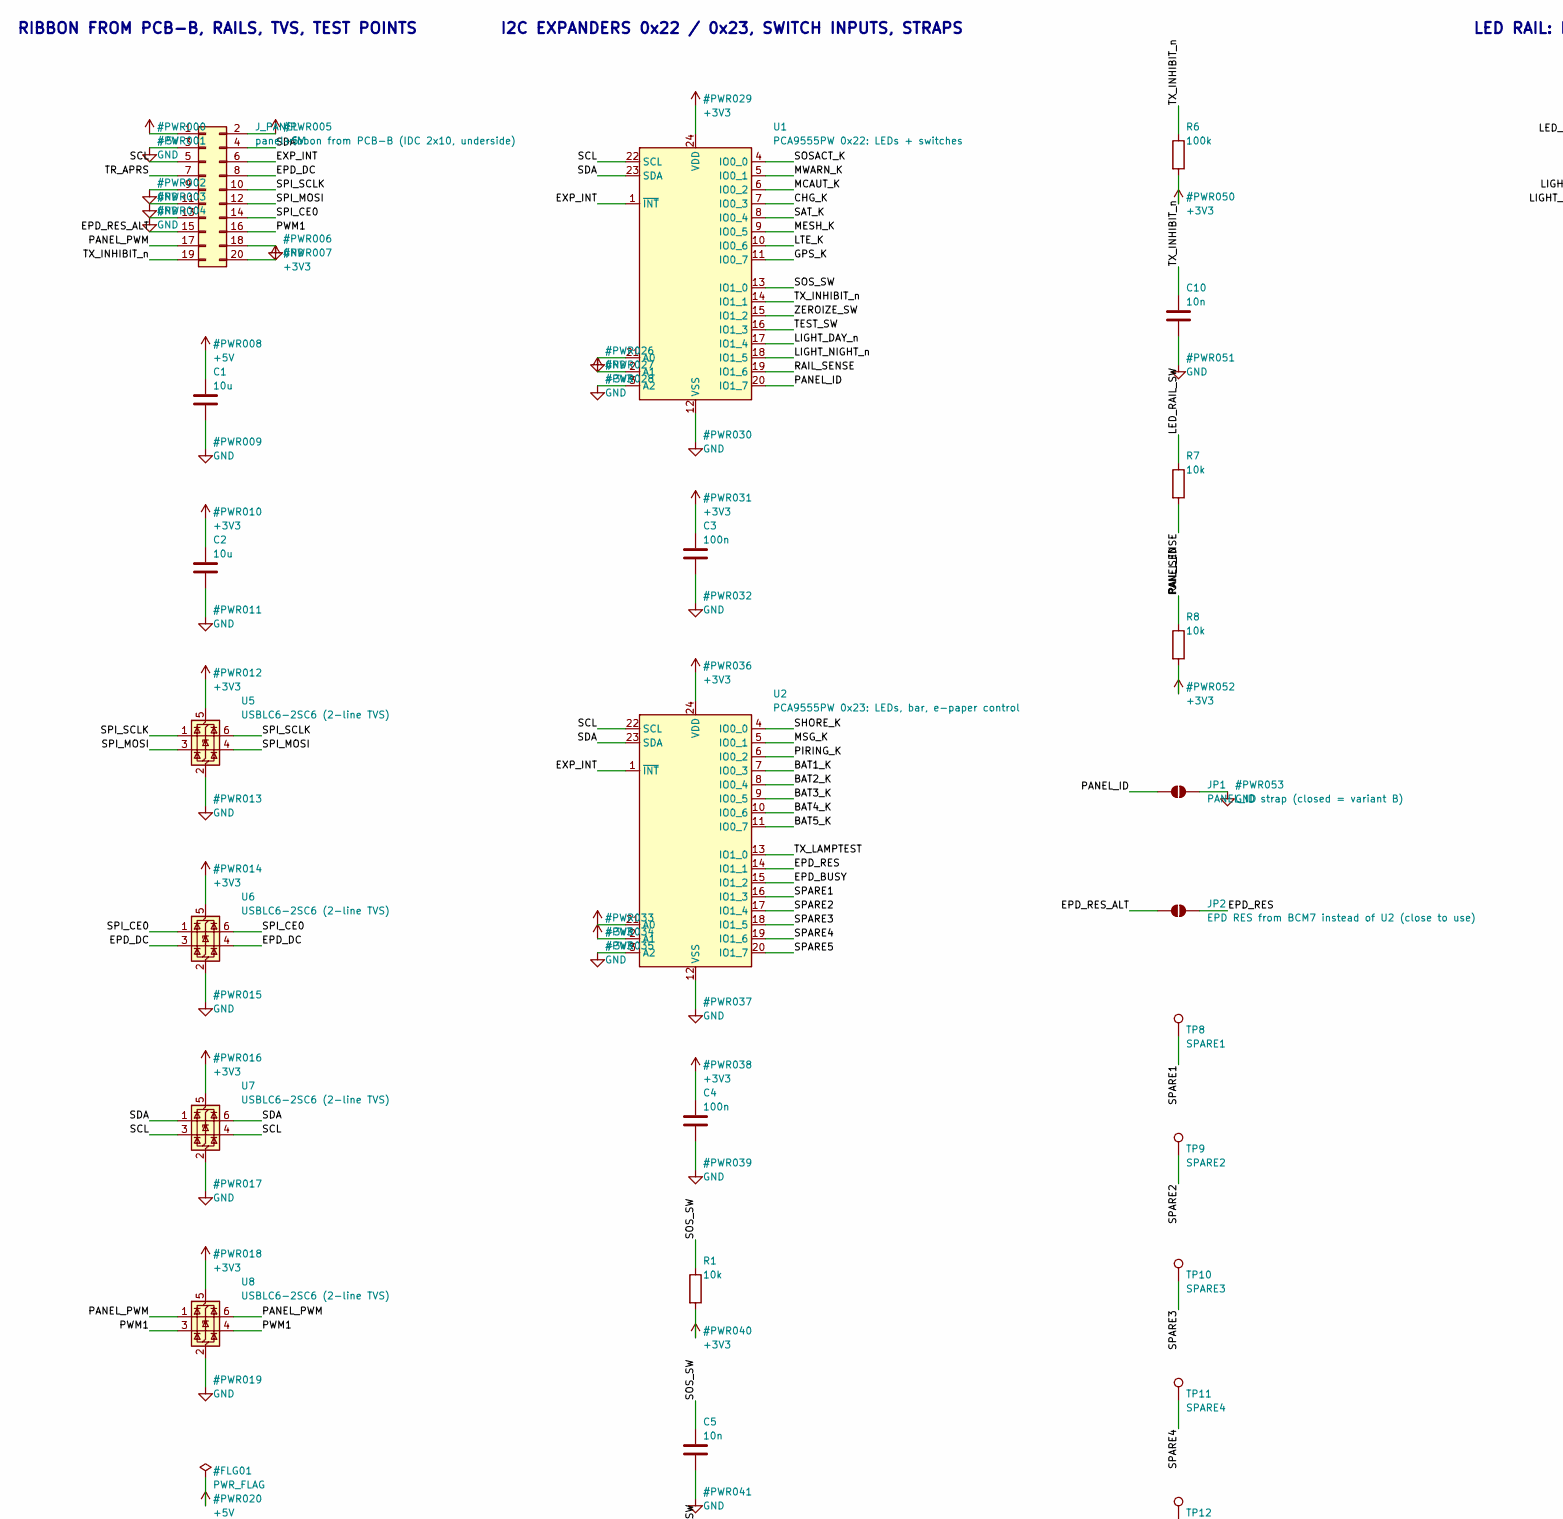
[picture p315: schematic pcb-c-display.kicad_sch, MeshSat Field Kit carrier - PCB-C CONTROL PANEL, part in row 1, column 1]

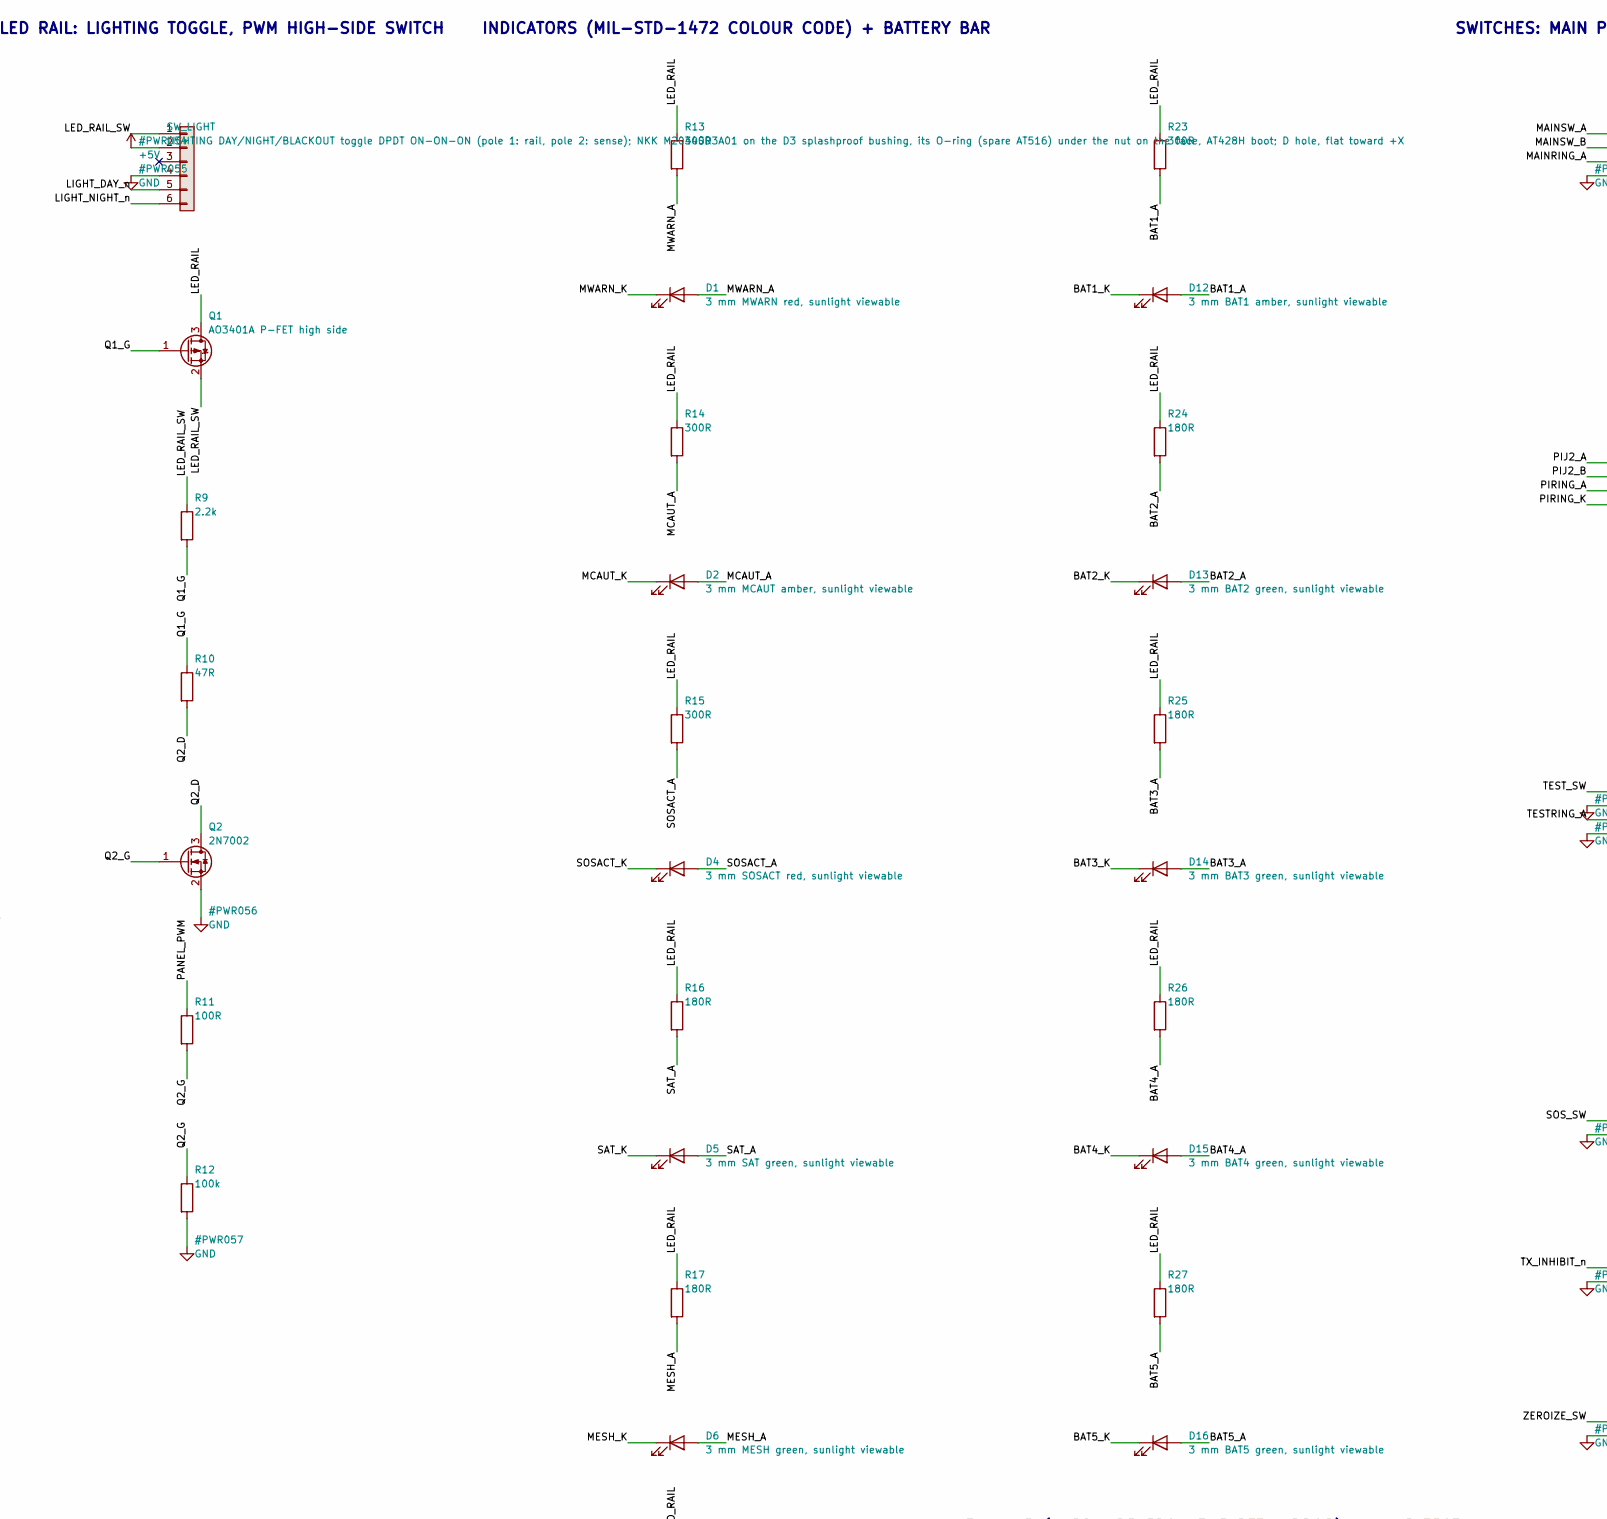
[picture p316: schematic pcb-c-display.kicad_sch, MeshSat Field Kit carrier - PCB-C CONTROL PANEL, part in row 1, column 2]

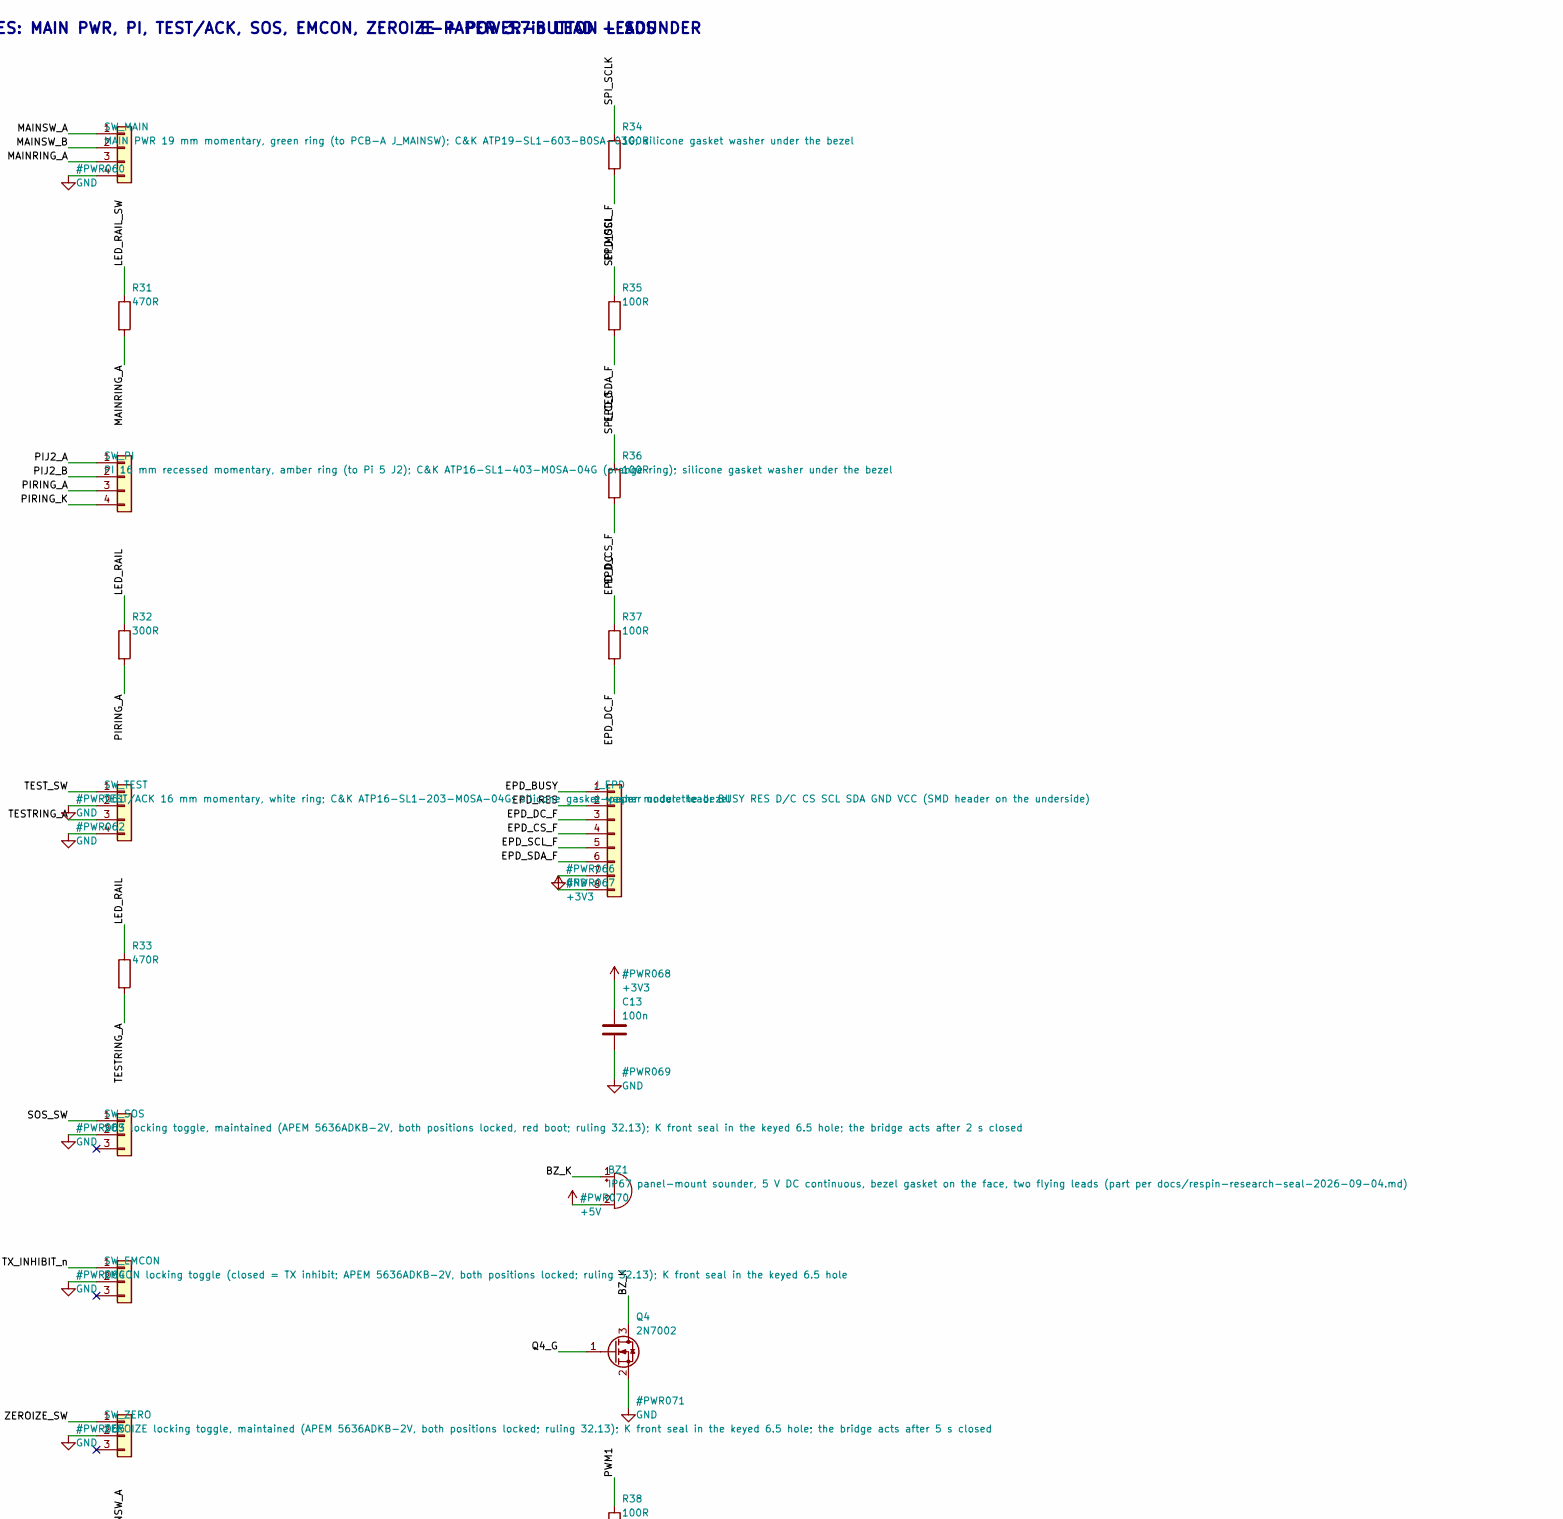
[picture p317: schematic pcb-c-display.kicad_sch, MeshSat Field Kit carrier - PCB-C CONTROL PANEL, part in row 1, column 3]

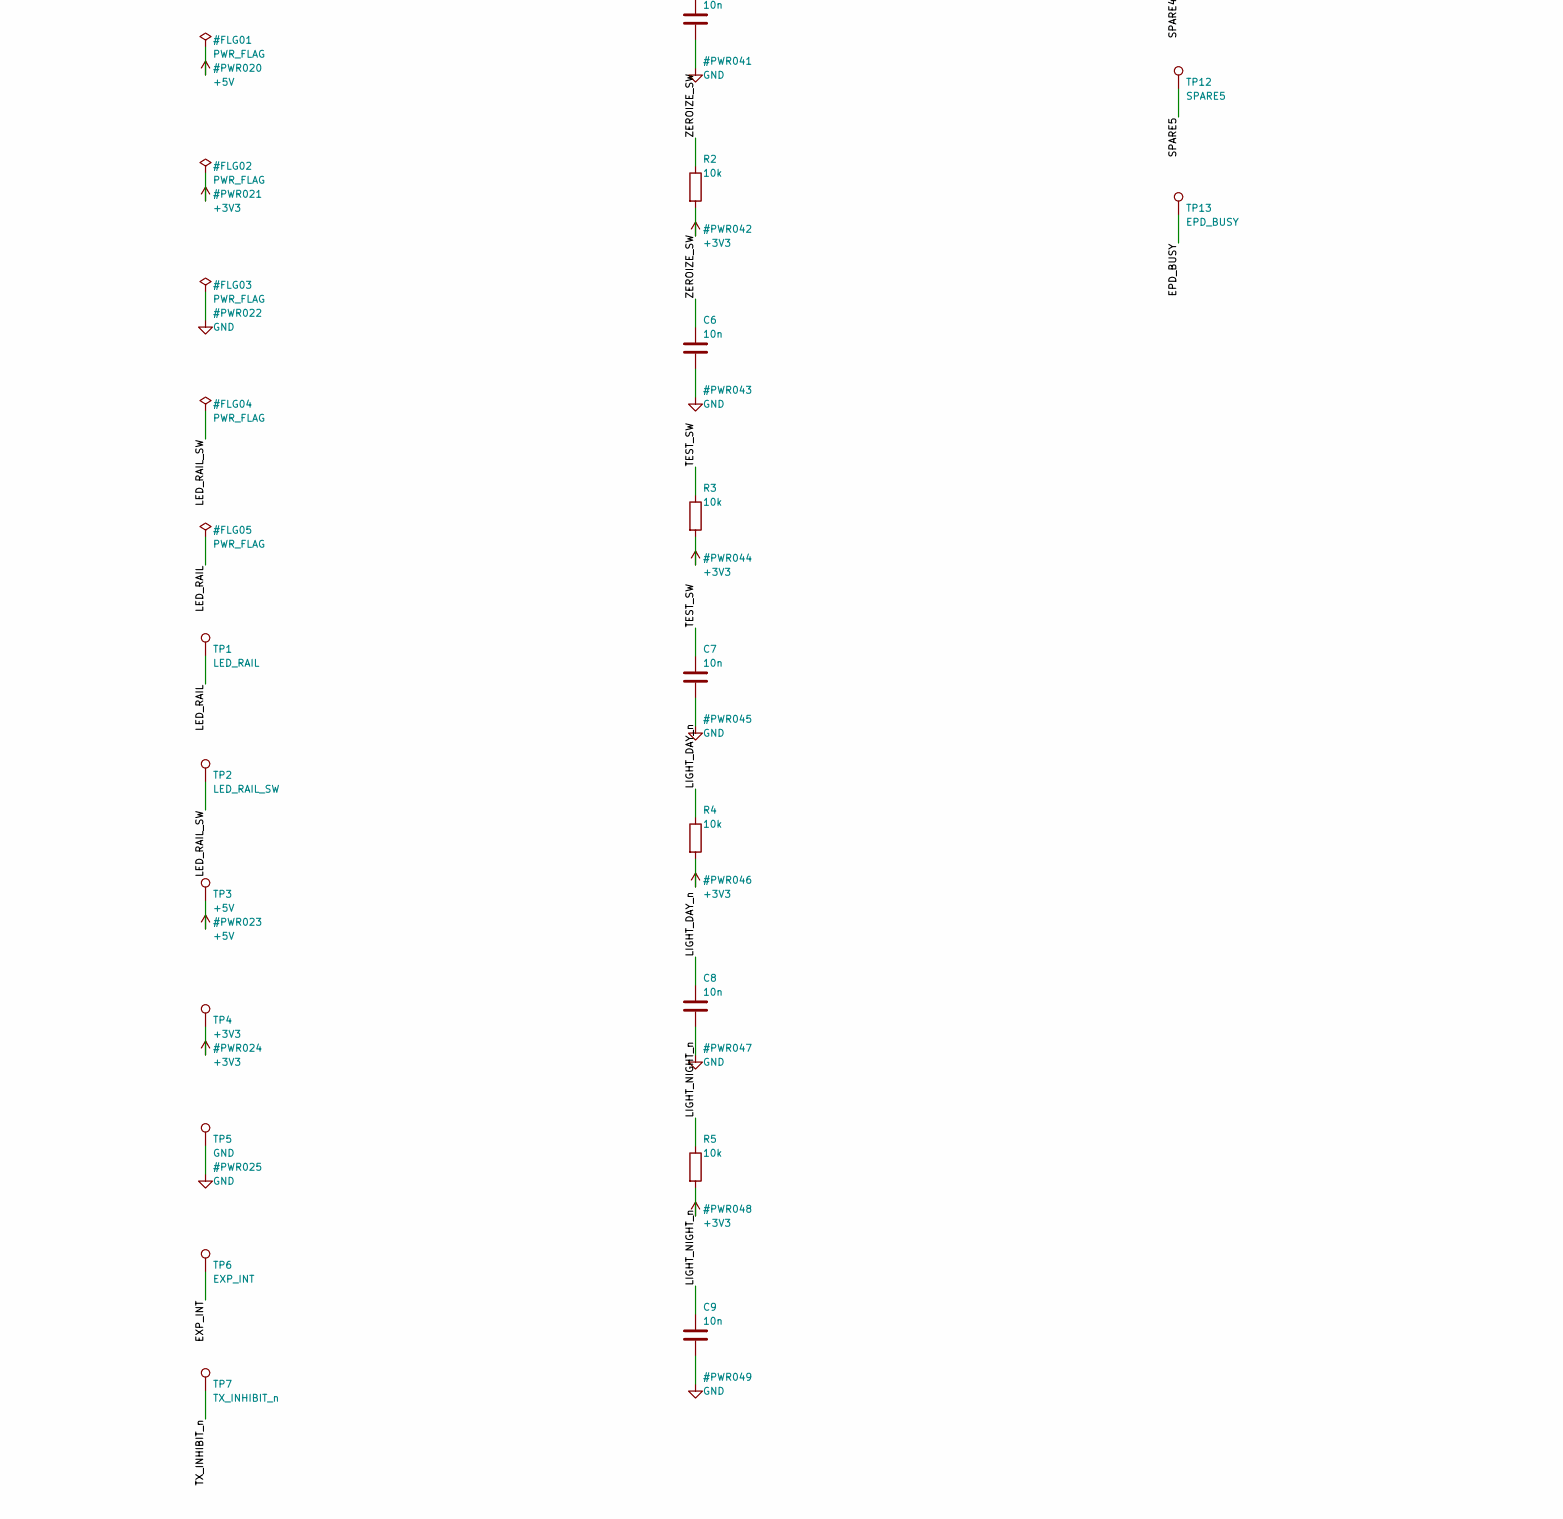
[picture p318: schematic pcb-c-display.kicad_sch, MeshSat Field Kit carrier - PCB-C CONTROL PANEL, part in row 2, column 1]

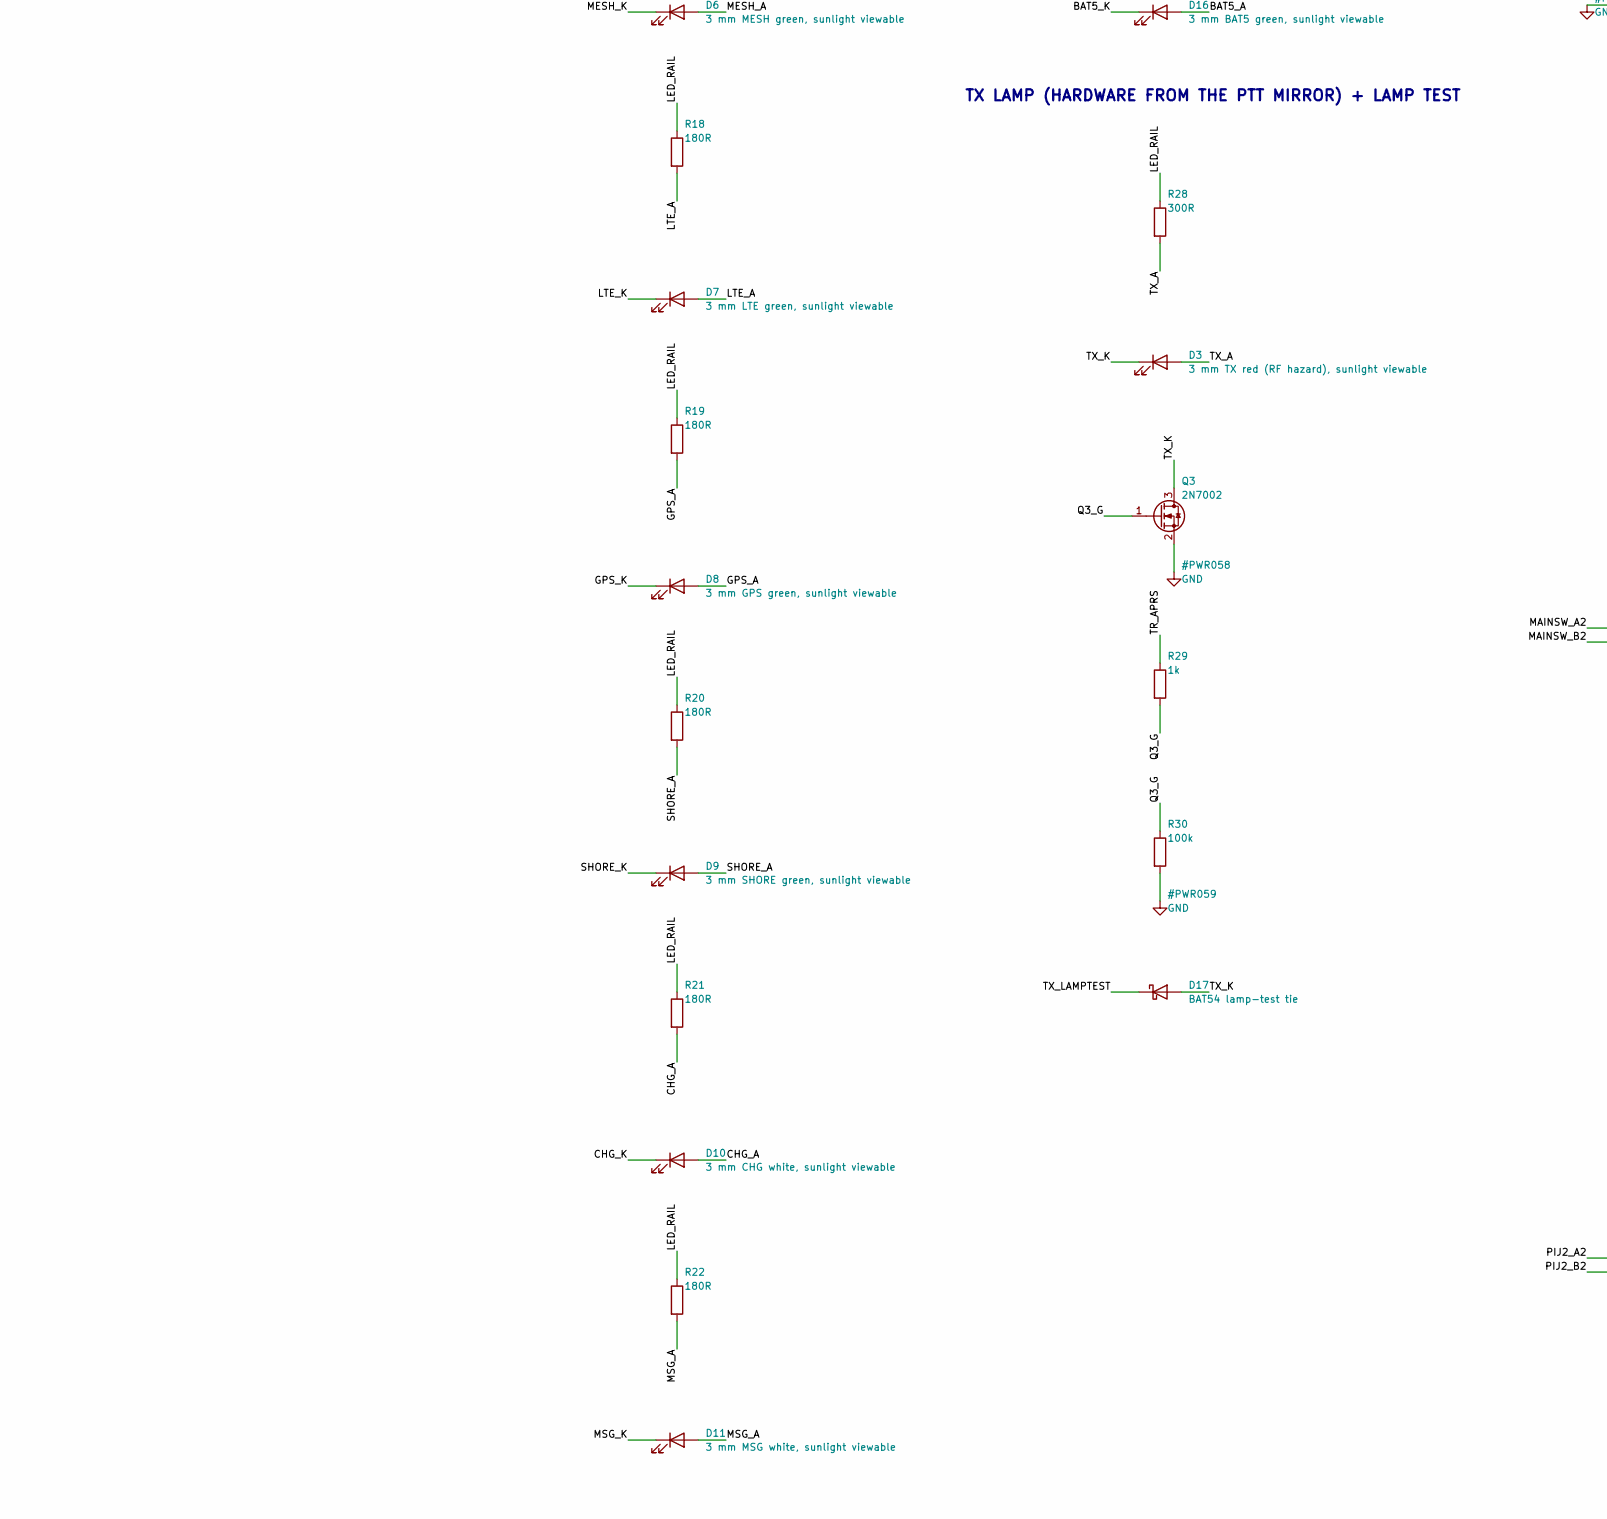
[picture p319: schematic pcb-c-display.kicad_sch, MeshSat Field Kit carrier - PCB-C CONTROL PANEL, part in row 2, column 2]

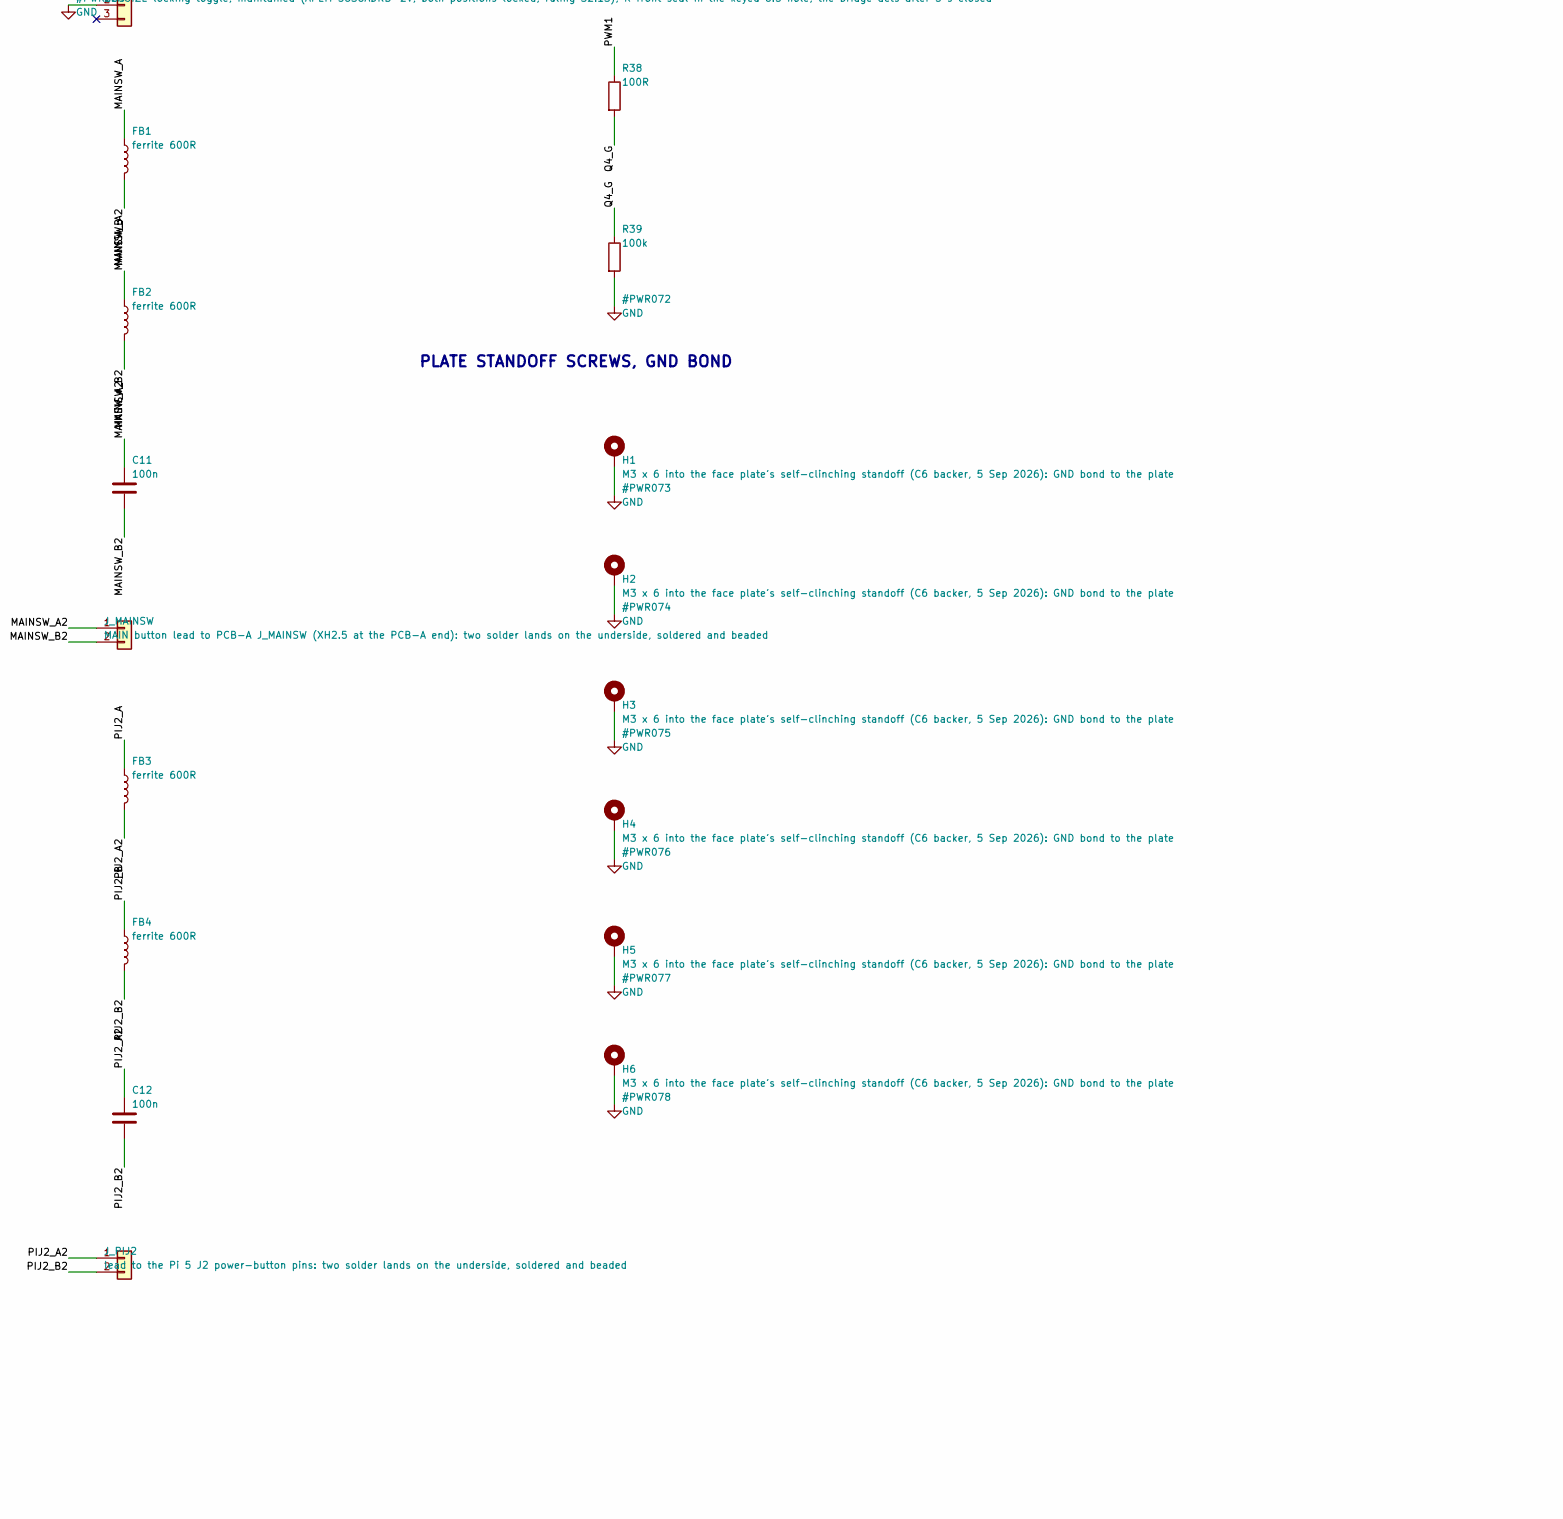
[picture p320: schematic pcb-c-display.kicad_sch, MeshSat Field Kit carrier - PCB-C CONTROL PANEL, part in row 2, column 3]

Parts:
BZ1: IP67 panel-mount sounder, 5 V DC continuous, beze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; PanelSounder
C1, C2: 10u; C_0805_2012Metric; LCSC C15850
C3, C4, C11, C12, C13: 100n; C_0603_1608Metric; LCSC C14663
C5, C6, C7, C8, C9, C10: 10n; C_0603_1608Metric; LCSC C57112
D1: 3 mm MWARN red, sunlight viewable; LED_D3.0mm
D2: 3 mm MCAUT amber, sunlight viewable; LED_D3.0mm
D3: 3 mm TX red (RF hazard), sunlight viewable; LED_D3.0mm
D4: 3 mm SOSACT red, sunlight viewable; LED_D3.0mm
D5: 3 mm SAT green, sunlight viewable; LED_D3.0mm
D6: 3 mm MESH green, sunlight viewable; LED_D3.0mm
D7: 3 mm LTE green, sunlight viewable; LED_D3.0mm
D8: 3 mm GPS green, sunlight viewable; LED_D3.0mm
D9: 3 mm SHORE green, sunlight viewable; LED_D3.0mm
D10: 3 mm CHG white, sunlight viewable; LED_D3.0mm
D11: 3 mm MSG white, sunlight viewable; LED_D3.0mm
D12: 3 mm BAT1 amber, sunlight viewable; LED_D3.0mm
D13: 3 mm BAT2 green, sunlight viewable; LED_D3.0mm
D14: 3 mm BAT3 green, sunlight viewable; LED_D3.0mm
D15: 3 mm BAT4 green, sunlight viewable; LED_D3.0mm
D16: 3 mm BAT5 green, sunlight viewable; LED_D3.0mm
D17: BAT54 lamp-test tie; D_SOD-123; LCSC C2166
FB1, FB2, FB3, FB4: ferrite 600R; L_0603_1608Metric; LCSC C1017
H1, H2, H3, H4, H5, H6: M3 x 6 into the face plate's self-clinching stand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; BackerScrew_M3_GND
JP1: PANEL_ID strap (closed = variant B); SolderJumper-2_P1.3mm_Open_RoundedPad1.0x1.5mm
JP2: EPD RES from BCM7 instead of U2 (close to use); SolderJumper-2_P1.3mm_Open_RoundedPad1.0x1.5mm
J_EPD: e-paper module lead: BUSY RES D/C CS SCL SDA GND 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; PinHeader_1x08_P2.54mm_Vertical_SMD_Pin1Left
J_MAINSW: MAIN button lead to PCB-A J_MAINSW (XH2.5 at the 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; LeadLands_1x02
J_PANEL: panel ribbon from PCB-B (IDC 2x10, underside); IDC-Header_2x10_P2.54mm_Vertical_SMD
J_PIJ2: lead to the Pi 5 J2 power-button pins: two solder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; LeadLands_1x02
Q1: AO3401A P-FET high side; SOT-23; LCSC C15127
Q2, Q3, Q4: 2N7002; SOT-23; LCSC C8545
R1, R2, R3, R4, R5, R7, R8: 10k; R_0603_1608Metric; LCSC C25804
R6, R12, R30, R39: 100k; R_0603_1608Metric; LCSC C25803
R9: 2.2k; R_0603_1608Metric; LCSC C4190
R10: 47R; R_0603_1608Metric; LCSC C25118
R11, R34, R35, R36, R37, R38: 100R; R_0603_1608Metric; LCSC C22775
R13, R14, R15, R23, R28, R32: 300R; R_0603_1608Metric; LCSC C23025
R16, R17, R18, R19, R20, R21, R22, R24, R25, R26, R27: 180R; R_0603_1608Metric; LCSC C25270
R29: 1k; R_0603_1608Metric; LCSC C11702
R31, R33: 470R; R_0603_1608Metric; LCSC C23179
SW_EMCON: EMCON locking toggle (closed = TX inhibit; APEM 5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; ToggleBody_SPDT
SW_LIGHT: LIGHTING DAY/NIGHT/BLACKOUT toggle DPDT ON-ON-ON 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; ToggleBody_DPDT
SW_MAIN: MAIN PWR 19 mm momentary, green ring (to PCB-A J_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; PanelSwitch_19mm
SW_PI: PI 16 mm recessed momentary, amber ring (to Pi 5 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; PanelSwitch_16mm
SW_SOS: SOS locking toggle, maintained (APEM 5636ADKB-2V,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; ToggleBody_SPDT
SW_TEST: TEST/ACK 16 mm momentary, white ring; C&K ATP16-S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; PanelSwitch_16mm
SW_ZERO: ZEROIZE locking toggle, maintained (APEM 5636ADKB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; ToggleBody_SPDT
TP1: LED_RAIL; TestPoint_Pad_D1.5mm
TP2: LED_RAIL_SW; TestPoint_Pad_D1.5mm
TP3: +5V; TestPoint_Pad_D1.5mm
TP4: +3V3; TestPoint_Pad_D1.5mm
TP5: GND; TestPoint_Pad_D1.5mm
TP6: EXP_INT; TestPoint_Pad_D1.5mm
TP7: TX_INHIBIT_n; TestPoint_Pad_D1.5mm
TP8: SPARE1; TestPoint_Pad_D1.5mm
TP9: SPARE2; TestPoint_Pad_D1.5mm
TP10: SPARE3; TestPoint_Pad_D1.5mm
TP11: SPARE4; TestPoint_Pad_D1.5mm
TP12: SPARE5; TestPoint_Pad_D1.5mm
TP13: EPD_BUSY; TestPoint_Pad_D1.5mm
U1: PCA9555PW 0x22: LEDs + switches; TSSOP-24_4.4x7.8mm_P0.65mm; LCSC C50993
U2: PCA9555PW 0x23: LEDs, bar, e-paper control; TSSOP-24_4.4x7.8mm_P0.65mm; LCSC C50993
U5, U6, U7, U8: USBLC6-2SC6 (2-line TVS); SOT-23-6; LCSC C7519

Connections:
+3V3: C2.1, C3.1, C4.1, C13.1, J_EPD.8, J_PANEL.20, R1.2, R2.2, R3.2, R4.2, R5.2, R6.2, R8.2, TP4.1, U1.2 (A1), U1.24 (VDD), U2.2 (A1), U2.21 (A0), U2.24 (VDD), U5.5 (VBUS), U6.5 (VBUS), U7.5 (VBUS), U8.5 (VBUS)
+5V: BZ1.2 (-), C1.1, J_PANEL.1, J_PANEL.2, SW_LIGHT.2, TP3.1
/BAT1_A: D12.2 (A), R23.2
/BAT1_K: D12.1 (K), U2.7 (IO0_3)
/BAT2_A: D13.2 (A), R24.2
/BAT2_K: D13.1 (K), U2.8 (IO0_4)
/BAT3_A: D14.2 (A), R25.2
/BAT3_K: D14.1 (K), U2.9 (IO0_5)
/BAT4_A: D15.2 (A), R26.2
/BAT4_K: D15.1 (K), U2.10 (IO0_6)
/BAT5_A: D16.2 (A), R27.2
/BAT5_K: D16.1 (K), U2.11 (IO0_7)
/BZ_K: BZ1.1 (+), Q4.3 (D)
/CHG_A: D10.2 (A), R21.2
/CHG_K: D10.1 (K), U1.7 (IO0_3)
/EPD_BUSY: J_EPD.1, TP13.1, U2.15 (IO1_2)
/EPD_CS_F: J_EPD.4, R36.2
/EPD_DC: J_PANEL.8, R37.1, U6.3 (I/O2), U6.4 (I/O2)
/EPD_DC_F: J_EPD.3, R37.2
/EPD_RES: JP2.2 (B), J_EPD.2, U2.14 (IO1_1)
/EPD_RES_ALT: JP2.1 (A), J_PANEL.15
/EPD_SCL_F: J_EPD.5, R34.2
/EPD_SDA_F: J_EPD.6, R35.2
/EXP_INT: J_PANEL.6, TP6.1, U1.1 (~INT), U2.1 (~INT)
/GPS_A: D8.2 (A), R19.2
/GPS_K: D8.1 (K), U1.11 (IO0_7)
/LED_RAIL: Q1.3 (D), R13.1, R14.1, R15.1, R16.1, R17.1, R18.1, R19.1, R20.1, R21.1, R22.1, R23.1, R24.1, R25.1, R26.1, R27.1, R28.1, R32.1, R33.1, TP1.1
/LED_RAIL_SW: Q1.2 (S), R7.1, R9.1, R31.1, SW_LIGHT.1, TP2.1
/LIGHT_DAY_n: C8.1, R4.1, SW_LIGHT.5, U1.17 (IO1_4)
/LIGHT_NIGHT_n: C9.1, R5.1, SW_LIGHT.6, U1.18 (IO1_5)
/LTE_A: D7.2 (A), R18.2
/LTE_K: D7.1 (K), U1.10 (IO0_6)
/MAINRING_A: R31.2, SW_MAIN.3
/MAINSW_A: FB1.1, SW_MAIN.1
/MAINSW_A2: C11.1, FB1.2, J_MAINSW.1
/MAINSW_B: FB2.1, SW_MAIN.2
/MAINSW_B2: C11.2, FB2.2, J_MAINSW.2
/MCAUT_A: D2.2 (A), R14.2
/MCAUT_K: D2.1 (K), U1.6 (IO0_2)
/MESH_A: D6.2 (A), R17.2
/MESH_K: D6.1 (K), U1.9 (IO0_5)
/MSG_A: D11.2 (A), R22.2
/MSG_K: D11.1 (K), U2.5 (IO0_1)
/MWARN_A: D1.2 (A), R13.2
/MWARN_K: D1.1 (K), U1.5 (IO0_1)
/PANEL_ID: JP1.1 (A), R8.1, U1.20 (IO1_7)
/PANEL_PWM: J_PANEL.17, R11.1, U8.1 (I/O1), U8.6 (I/O1)
/PIJ2_A: FB3.1, SW_PI.1
/PIJ2_A2: C12.1, FB3.2, J_PIJ2.1
/PIJ2_B: FB4.1, SW_PI.2
/PIJ2_B2: C12.2, FB4.2, J_PIJ2.2
/PIRING_A: R32.2, SW_PI.3
/PIRING_K: SW_PI.4, U2.6 (IO0_2)
/PWM1: J_PANEL.16, R38.1, U8.3 (I/O2), U8.4 (I/O2)
/Q1_G: Q1.1 (G), R9.2, R10.1
/Q2_D: Q2.3 (D), R10.2
/Q2_G: Q2.1 (G), R11.2, R12.1
/Q3_G: Q3.1 (G), R29.2, R30.1
/Q4_G: Q4.1 (G), R38.2, R39.1
/RAIL_SENSE: R7.2, U1.19 (IO1_6)
/SAT_A: D5.2 (A), R16.2
/SAT_K: D5.1 (K), U1.8 (IO0_4)
/SCL: J_PANEL.5, U1.22 (SCL), U2.22 (SCL), U7.3 (I/O2), U7.4 (I/O2)
/SDA: J_PANEL.4, U1.23 (SDA), U2.23 (SDA), U7.1 (I/O1), U7.6 (I/O1)
/SHORE_A: D9.2 (A), R20.2
/SHORE_K: D9.1 (K), U2.4 (IO0_0)
/SOSACT_A: D4.2 (A), R15.2
/SOSACT_K: D4.1 (K), U1.4 (IO0_0)
/SOS_SW: C5.1, R1.1, SW_SOS.1, U1.13 (IO1_0)
/SPARE1: TP8.1, U2.16 (IO1_3)
/SPARE2: TP9.1, U2.17 (IO1_4)
/SPARE3: TP10.1, U2.18 (IO1_5)
/SPARE4: TP11.1, U2.19 (IO1_6)
/SPARE5: TP12.1, U2.20 (IO1_7)
/SPI_CE0: J_PANEL.14, R36.1, U6.1 (I/O1), U6.6 (I/O1)
/SPI_MOSI: J_PANEL.12, R35.1, U5.3 (I/O2), U5.4 (I/O2)
/SPI_SCLK: J_PANEL.10, R34.1, U5.1 (I/O1), U5.6 (I/O1)
/TESTRING_A: R33.2, SW_TEST.3
/TEST_SW: C7.1, R3.1, SW_TEST.1, U1.16 (IO1_3)
/TR_APRS: J_PANEL.7, R29.1
/TX_A: D3.2 (A), R28.2
/TX_INHIBIT_n: C10.1, J_PANEL.19, R6.1, SW_EMCON.1, TP7.1, U1.14 (IO1_1)
/TX_K: D3.1 (K), D17.2 (A), Q3.3 (D)
/TX_LAMPTEST: D17.1 (K), U2.13 (IO1_0)
/ZEROIZE_SW: C6.1, R2.1, SW_ZERO.1, U1.15 (IO1_2)
GND: C1.2, C2.2, C3.2, C4.2, C5.2, C6.2, C7.2, C8.2, C9.2, C10.2, C13.2, H1.1, H2.1, H3.1, H4.1, H5.1, H6.1, JP1.2 (B), J_EPD.7, J_PANEL.3, J_PANEL.9, J_PANEL.11, J_PANEL.13, J_PANEL.18, Q2.2 (S), Q3.2 (S), Q4.2 (S), R12.2, R30.2, R39.2, SW_EMCON.2, SW_LIGHT.4, SW_MAIN.4, SW_SOS.2, SW_TEST.2, SW_TEST.4, SW_ZERO.2, TP5.1, U1.3 (A2), U1.12 (VSS), U1.21 (A0), U2.3 (A2), U2.12 (VSS), U5.2 (GND), U6.2 (GND), U7.2 (GND), U8.2 (GND)

Notes on the sheet:
RIBBON FROM PCB-B, RAILS, TVS, TEST POINTS
I2C EXPANDERS 0x22 / 0x23, SWITCH INPUTS, STRAPS
LED RAIL: LIGHTING TOGGLE, PWM HIGH-SIDE SWITCH
INDICATORS (MIL-STD-1472 COLOUR CODE) + BATTERY BAR
TX LAMP (HARDWARE FROM THE PTT MIRROR) + LAMP TEST
SWITCHES: MAIN PWR, PI, TEST/ACK, SOS, EMCON, ZEROIZE + POWER-BUTTON LEADS
E-PAPER 3.7in LEAD + SOUNDER
PLATE STANDOFF SCREWS, GND BOND

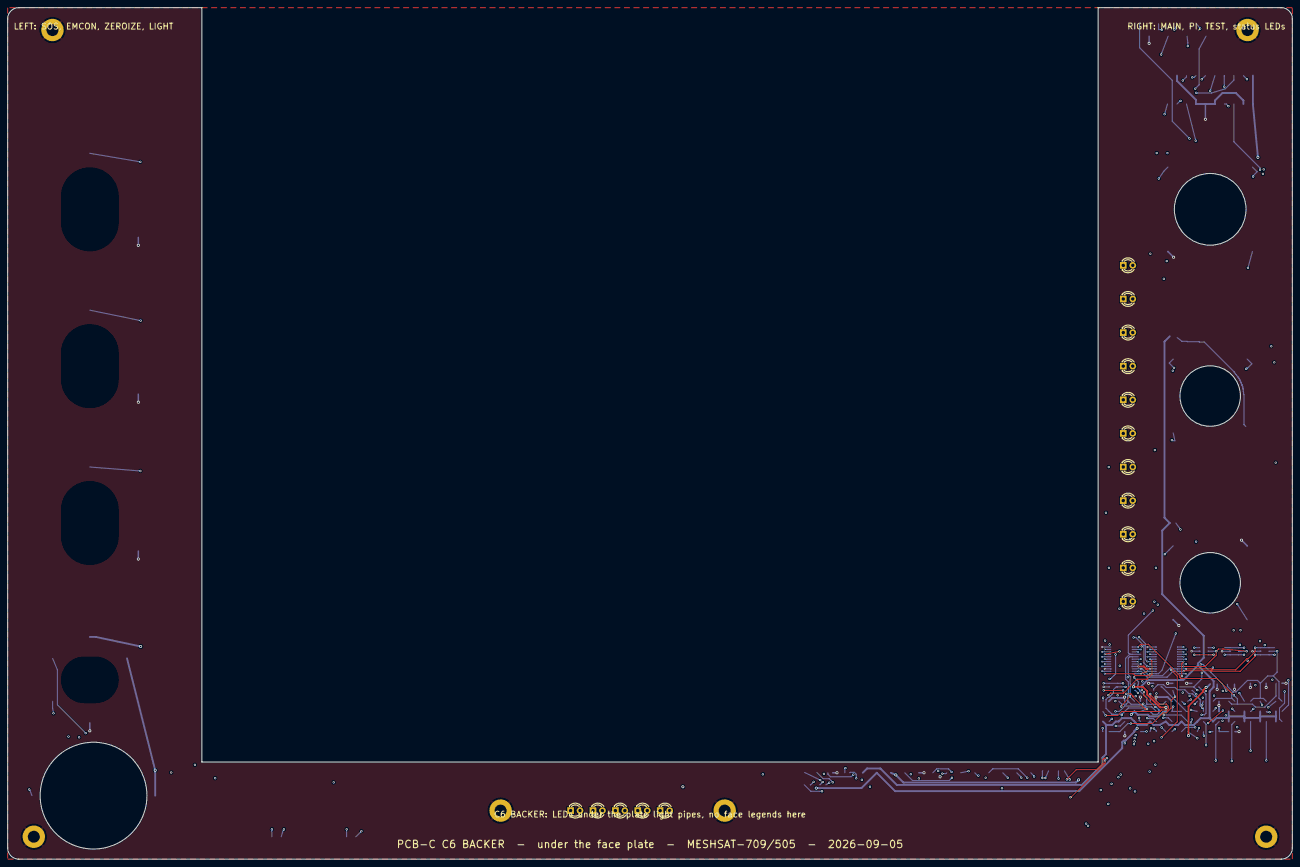
[picture p321: board v2/release/revA/boards/meshsat-pcb-c-revA-C6/pcb-c-display.kicad_pcb from above]

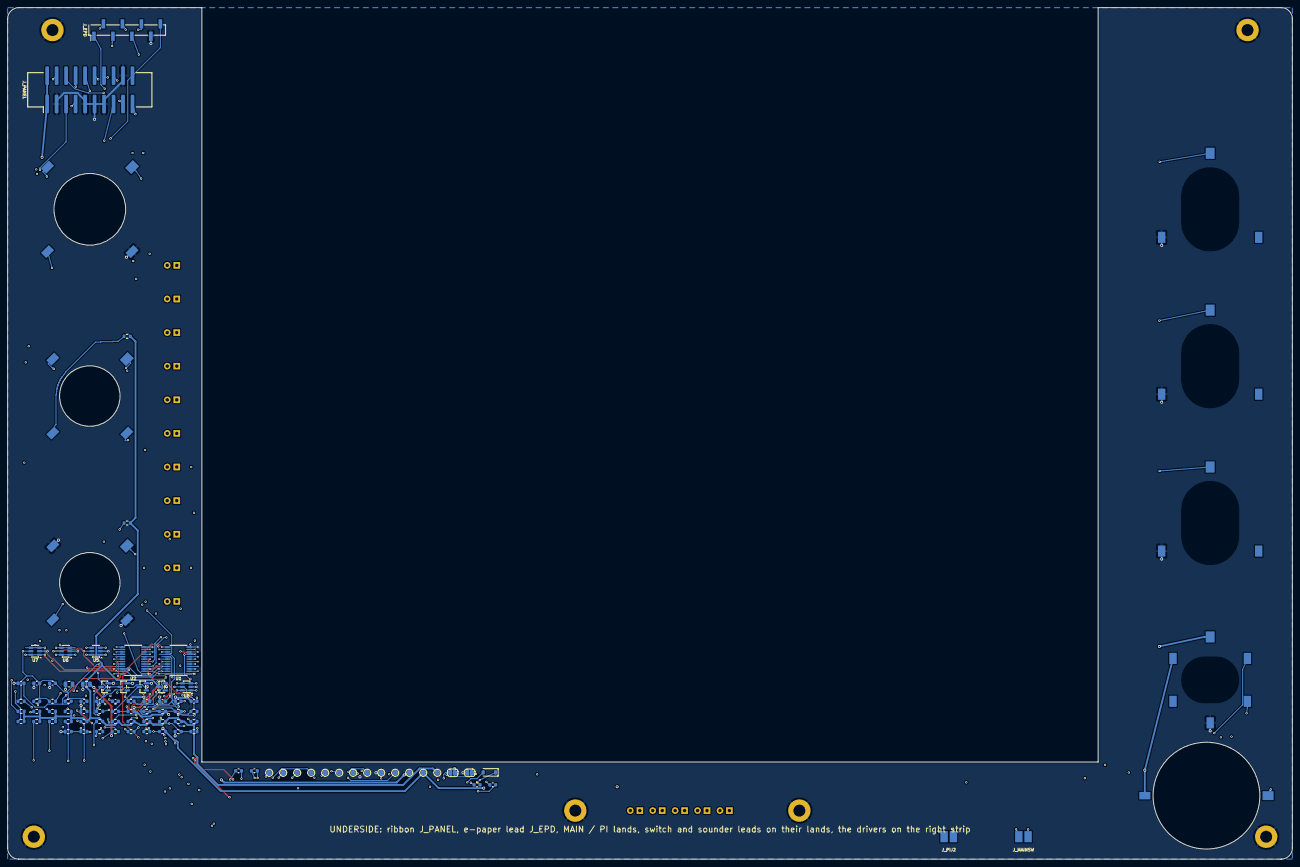
[picture p322: board v2/release/revA/boards/meshsat-pcb-c-revA-C6/pcb-c-display.kicad_pcb from below]

Board: 4 copper layers, 344.0 x 228.0 mm, 116 parts (86 on the bottom side), 86 nets.
