meshsat/meshsat-fieldkit/v2/release/review-packets/C-C24-1f614233/native/pcb-c-display.kicad_sch

## KiCad design v2/release/review-packets/C-C24-1f614233/native/pcb-c-display.kicad_sch (2026-09-26)

Schematic: pcb-c-display.kicad_sch

Parts:
BZ1: IP67 panel-mount sounder, 5 V DC continuous, beze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; PanelSounder
C1, C2: 10u; C_0805_2012Metric; LCSC C15850
C3, C4, C14, C15, C16: 1u; C_0603_1608Metric
C5, C6: 15p NP0; C_0402_1005Metric
C7, C8, C9, C10, C11, C12, C13, C25, C29, C38: 100n; C_0603_1608Metric
C17, C18, C26, C27, C39: 100n; C_0603_1608Metric; LCSC C14663
C19, C20, C21, C22, C23, C24: 10n; C_0603_1608Metric; LCSC C57112
C28: 4.7u; C_0805_2012Metric
C30, C32, C33, C34, C35, C36, C37: 1u 25V; C_0603_1608Metric
C31: 4.7u 25V; C_0603_1608Metric; LCSC C90057
CAM_H1, CAM_H2: M2 screw of the USB camera module (25 x 25 board,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; MountingHole_2.2mm_M2
D1: 3 mm MWARN red, sunlight viewable; LED_D3.0mm
D2: 3 mm MCAUT amber, sunlight viewable; LED_D3.0mm
D3: 3 mm TX red (RF hazard), sunlight viewable; LED_D3.0mm
D4: 3 mm SOSACT red, sunlight viewable; LED_D3.0mm
D5: 3 mm SAT green, sunlight viewable; LED_D3.0mm
D6: 3 mm MESH green, sunlight viewable; LED_D3.0mm
D7: 3 mm LTE green, sunlight viewable; LED_D3.0mm
D8: 3 mm GPS green, sunlight viewable; LED_D3.0mm
D9: 3 mm SHORE green, sunlight viewable; LED_D3.0mm
D10: 3 mm CHG white, sunlight viewable; LED_D3.0mm
D11: 3 mm MSG white, sunlight viewable; LED_D3.0mm
D12: 3 mm BAT1 amber, sunlight viewable; LED_D3.0mm
D13: 3 mm BAT2 green, sunlight viewable; LED_D3.0mm
D14: 3 mm BAT3 green, sunlight viewable; LED_D3.0mm
D15: 3 mm BAT4 green, sunlight viewable; LED_D3.0mm
D16: 3 mm BAT5 green, sunlight viewable; LED_D3.0mm
D17: BAT54 lamp-test tie; D_SOD-123; LCSC C7502705
D18: status (GPIO25); LED_0603_1608Metric
D19: SS2040FL: EPD_SW -> VGH; D_SOD-123F; LCSC C268712
D20: SS2040FL: pump clamp; D_SOD-123F; LCSC C268712
D21: SS2040FL: pump -> VGL; D_SOD-123F; LCSC C268712
FB1, FB2, FB3, FB4: ferrite 600R; L_0603_1608Metric; LCSC C1002
H1, H2, H3, H4, H5, H6, H7, H8: M3 x 6 into the face plate's self-clinching stand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; BackerScrew_M3_GND
JP1: BOOTSEL: short while powering to enter the USB bo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; SolderJumper-2_P1.3mm_Open_RoundedPad1.0x1.5mm
JP2: PANEL_ID strap (closed = variant B); SolderJumper-2_P1.3mm_Open_RoundedPad1.0x1.5mm
J_EPD: Hirose FH34SRJ-24S-0.5SH ZIF for the E2370KS0C1 f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; Hirose_FH34SRJ-24S
J_HSJ1: U-174/U headset jack 1 (Amphenol Nexus class, dra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; PanelJack_17mm
J_HSJ2: U-174/U headset jack 2 (Amphenol Nexus class, dra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; PanelJack_17mm
J_MAINSW: MAIN button lead to A22 J_MAINSW (XH2.5 at the A2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; LeadLands_1x02
J_PANEL: panel ribbon from B16 J_PANEL (IDC 2x13 SMD, unde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; IDC-Header_2x13_P2.54mm_Vertical_SMD
J_PIJ2: PI button lead: two solder lands on the underside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; LeadLands_1x02
L1: 10uH ATNR4010100MT 0.8 A (the boost inductor); L_APV_ANR4020
Q1: AO3401A P-FET high side; SOT-23; LCSC C15127
Q2, Q3, Q4: 2N7002; SOT-23; LCSC C8545
Q5: AO3401A P-FET: the e-paper's supply switch (EPD_P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; SOT-23; LCSC C15127
Q6: Si2300DS-T1-GE3 N-FET (Vishay, SOT-23, G S D like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; SOT-23; LCSC C72271
R1, R6: 1k; R_0603_1608Metric
R2, R3: 27R; R_0603_1608Metric
R4, R42: 10k; R_0603_1608Metric
R5: 1k (BOOTSEL); R_0603_1608Metric
R7, R8: 2.2k; R_0603_1608Metric
R9, R10, R11, R12, R13, R14, R15, R16: 10k; R_0603_1608Metric; LCSC C25804
R17: 2.2k; R_0603_1608Metric; LCSC C4190
R18: 47R; R_0603_1608Metric; LCSC C23182
R19, R44: 100R; R_0603_1608Metric; LCSC C22775
R20, R38, R45: 100k; R_0603_1608Metric; LCSC C25803
R21, R22, R23, R31, R36, R40: 300R; R_0603_1608Metric; LCSC C23025
R24, R25, R26, R27, R28, R29, R30, R32, R33, R34, R35: 180R; R_0603_1608Metric; LCSC C22828
R37: 1k; R_0603_1608Metric; LCSC C21190
R39, R41: 470R; R_0603_1608Metric; LCSC C23179
R43: 0.47R 1%; R_0603_1608Metric
SW_EMCON: EMCON locking toggle (closed = TX inhibit, a hard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; ToggleBody_SPDT
SW_LIGHT: LIGHTING DAY/NIGHT/BLACKOUT toggle DPDT ON-ON-ON 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; ToggleBody_DPDT
SW_MAIN: MAIN PWR 19 mm momentary, green ring (to A22 J_MA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; PanelSwitch_19mm
SW_PI: PI 16 mm recessed momentary, amber ring (PI_SHDN_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; PanelSwitch_16mm
SW_SOS: SOS locking toggle, maintained (APEM 5636ADKB-2V,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; ToggleBody_SPDT
SW_TEST: TEST/ACK 16 mm momentary, white ring; C&K ATP16-S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; PanelSwitch_16mm
SW_ZERO: ZEROIZE locking toggle, maintained (APEM 5636ADKB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; ToggleBody_SPDT
TP1: SWCLK; TestPoint_Pad_D1.5mm
TP2: SWDIO; TestPoint_Pad_D1.5mm
TP3: C_RUN; TestPoint_Pad_D1.5mm
TP4: LED_RAIL; TestPoint_Pad_D1.5mm
TP5: LED_RAIL_SW; TestPoint_Pad_D1.5mm
TP6: +5V; TestPoint_Pad_D1.5mm
TP7: +3V3; TestPoint_Pad_D1.5mm
TP8: GND; TestPoint_Pad_D1.5mm
TP9: EXP_INT; TestPoint_Pad_D1.5mm
TP10: TX_INHIBIT_n; TestPoint_Pad_D1.5mm
TP11: EMCON_HW; TestPoint_Pad_D1.5mm
TP12: ZEROIZE_HW; TestPoint_Pad_D1.5mm
TP13: SPARE1; TestPoint_Pad_D1.5mm
TP14: SPARE2; TestPoint_Pad_D1.5mm
TP15: SPARE3; TestPoint_Pad_D1.5mm
TP16: SPARE4; TestPoint_Pad_D1.5mm
TP17: SPARE5; TestPoint_Pad_D1.5mm
TP18: SPARE6; TestPoint_Pad_D1.5mm
TP19: SPARE7; TestPoint_Pad_D1.5mm
TP20: SPARE8; TestPoint_Pad_D1.5mm
TP21: SPARE9; TestPoint_Pad_D1.5mm
TP22: SPARE10; TestPoint_Pad_D1.5mm
TP23: SPARE11; TestPoint_Pad_D1.5mm
TP24: SPARE12; TestPoint_Pad_D1.5mm
TP25: EPD_BUSY; TestPoint_Pad_D1.5mm
TP26: EPD_VGH; TestPoint_Pad_D1.5mm
TP27: EPD_VGL; TestPoint_Pad_D1.5mm
TP28: HB1; TestPoint_Pad_D1.5mm
TP29: HB2; TestPoint_Pad_D1.5mm
TP30: HB3; TestPoint_Pad_D1.5mm
TP31: SLOT_EN1; TestPoint_Pad_D1.5mm
TP32: SLOT_EN2; TestPoint_Pad_D1.5mm
TP33: SLOT_EN3; TestPoint_Pad_D1.5mm
TP34: HDMI_SEL1; TestPoint_Pad_D1.5mm
TP35: HDMI_SEL2; TestPoint_Pad_D1.5mm
TP36: PI_SHDN_REQ; TestPoint_Pad_D1.5mm
TP37: PI_KILL; TestPoint_Pad_D1.5mm
TP38: SHORE_INHIBIT; TestPoint_Pad_D1.5mm
TP39: PIJ2_A; TestPoint_Pad_D1.5mm
TP40: PIJ2_B; TestPoint_Pad_D1.5mm
TP41: ZEROIZE_SW; TestPoint_Pad_D1.5mm
TP42: SDA; TestPoint_Pad_D1.5mm
TP43: SCL; TestPoint_Pad_D1.5mm
TP44: SOS_SW; TestPoint_Pad_D1.5mm
TP45: TEST_SW; TestPoint_Pad_D1.5mm
TP46: TR_APRS; TestPoint_Pad_D1.5mm
TP47: C_DVDD; TestPoint_Pad_D1.5mm
TP48: BOOT_J; TestPoint_Pad_D1.5mm
U1: PCA9555PW 0x22: LED sinks, light mode inputs; TSSOP-24_4.4x7.8mm_P0.65mm; LCSC C2864778
U2: PCA9555PW 0x23: LED sinks, the battery bar, lamp 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; TSSOP-24_4.4x7.8mm_P0.65mm; LCSC C2864778
U3: RP2040 panel controller (USB device on B16's slot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; QFN-56-1EP_7x7mm_P0.4mm_EP3.2x3.2mm; LCSC C2040
U4: W25Q16JVUXIQ 16 Mbit QSPI flash (USON-8: 1 CS 2 D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; Winbond_USON-8-1EP_3x2mm_P0.5mm_EP0.2x1.6mm; LCSC C2843335
U5: TLV75533PDBV 3.3 V 500 mA LDO for the controller,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; SOT-23-5
U6, U7, U8, U10, U11: USBLC6-2SC6; SOT-23-6; LCSC C7519
U9, U12: 74LVC1G17 Schmitt-trigger non-inverting buffer (D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; SOT-23-5; LCSC C151394
U_LIGHT: Vishay VEML7700 ambient light sensor (1 SCL 2 VDD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; Vishay_VEML7700; LCSC C504893
Y1: 12 MHz ABM8-272-T3 (3225): 1 XIN, 3 XOUT, 2 and 4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; Crystal_SMD_3225-4Pin_3.2x2.5mm; LCSC C20625731

Connections:
+3V3: C2.1, C4.1, C7.1, C8.1, C9.1, C10.1, C11.1, C12.1, C13.1, C16.1, C17.1, C18.1, C25.1, C38.1, C39.1, Q5.2 (S), R4.2, R7.2, R8.2, R9.2, R10.2, R11.2, R12.2, R13.2, R14.2, R16.2, R42.2, TP7.1, U1.2 (A1), U1.24 (VDD), U2.2 (A1), U2.21 (A0), U2.24 (VDD), U3.1 (IOVDD), U3.10 (IOVDD), U3.22 (IOVDD), U3.33 (IOVDD), U3.42 (IOVDD), U3.43 (ADC_AVDD), U3.44 (VREG_VIN), U3.48 (USB_VDD), U3.49 (IOVDD), U4.8 (+3V3), U5.5 (+3V3), U6.5 (VBUS), U7.5 (VBUS), U8.5 (VBUS), U9.5 (+3V3), U10.5 (VBUS), U11.5 (VBUS), U12.5 (+3V3), U_LIGHT.2 (+3V3)
+5V: BZ1.2 (-), C1.1, C3.1, J_PANEL.1, J_PANEL.2, SW_LIGHT.2, TP6.1, U5.1 (+5V), U5.3 (+5V)
BAT1_A: D12.2 (A), R31.2
BAT1_K: D12.1 (K), U2.7 (IO0_3)
BAT2_A: D13.2 (A), R32.2
BAT2_K: D13.1 (K), U2.8 (IO0_4)
BAT3_A: D14.2 (A), R33.2
BAT3_K: D14.1 (K), U2.9 (IO0_5)
BAT4_A: D15.2 (A), R34.2
BAT4_K: D15.1 (K), U2.10 (IO0_6)
BAT5_A: D16.2 (A), R35.2
BAT5_K: D16.1 (K), U2.11 (IO0_7)
BOOT_J: JP1.1 (A), R5.2, TP48.1
BZ_K: BZ1.1 (+), Q4.3 (D)
CHG_A: D10.2 (A), R29.2
CHG_K: D10.1 (K), U1.7 (IO0_3)
C_DVDD: C14.1, C15.1, TP47.1, U3.23 (DVDD), U3.45 (VREG_VOUT), U3.50 (DVDD)
C_RUN: R4.1, TP3.1, U3.26 (RUN)
EMCON_HW: J_PANEL.8, TP11.1, U3.32 (GPIO21), U9.4 (EMCON_HW)
EPD_BUSY: J_EPD.9 (BUSY_N), TP25.1, U3.9 (GPIO7)
EPD_CS: J_EPD.12 (CSB), U3.7 (GPIO5)
EPD_DC: J_EPD.11 (DC), U3.6 (GPIO4)
EPD_GDR: J_EPD.2 (GDR), Q6.1 (G)
EPD_PUMP: C31.2, D20.2 (A), D21.1 (K)
EPD_PWR_n: Q5.1 (G), R42.1, U3.41 (GPIO29_A3)
EPD_RESE: J_EPD.3 (RESE), Q6.2 (S), R43.1
EPD_RST: J_EPD.10 (RST_N), U3.8 (GPIO6)
EPD_SCL: J_EPD.13 (SCL), U3.4 (GPIO2)
EPD_SDA: J_EPD.14 (SDA), U3.5 (GPIO3)
EPD_SW: C31.1, D19.2 (A), L1.2, Q6.3 (D)
EPD_VCC: C28.1, C29.1, J_EPD.15 (VDDIO), J_EPD.16 (VDD), L1.1, Q5.3 (D)
EPD_VCOM: C37.1, J_EPD.24 (VCOM)
EPD_VDDD: C34.1, J_EPD.18 (VDDD)
EPD_VDH: C35.1, J_EPD.20 (VDH)
EPD_VDHR: C33.1, J_EPD.5 (VDHR)
EPD_VDL: C36.1, J_EPD.22 (VDL)
EPD_VGH: C30.1, D19.1 (K), J_EPD.21 (VGH), TP26.1
EPD_VGL: C32.1, D21.2 (A), J_EPD.23 (VGL), TP27.1
EXP_INT: J_PANEL.6, TP9.1, U1.1 (~INT), U2.1 (~INT), U3.36 (GPIO24), U8.3 (I/O2), U8.4 (I/O2)
GND: C1.2, C2.2, C3.2, C4.2, C5.2, C6.2, C7.2, C8.2, C9.2, C10.2, C11.2, C12.2, C13.2, C14.2, C15.2, C16.2, C17.2, C18.2, C19.2, C20.2, C21.2, C22.2, C23.2, C24.2, C25.2, C28.2, C29.2, C30.2, C32.2, C33.2, C34.2, C35.2, C36.2, C37.2, C38.2, C39.2, D18.1 (K), D20.1 (K), H1.1, H2.1, H3.1, H4.1, H5.1, H6.1, H7.1, H8.1, JP1.2 (B), JP2.2 (B), J_EPD.8 (BS), J_EPD.17 (VSS), J_EPD.25 (SHIELD), J_EPD.26 (SHIELD), J_PANEL.3, J_PANEL.9, J_PANEL.14, J_PANEL.17, Q2.2 (S), Q3.2 (S), Q4.2 (S), R20.2, R38.2, R43.2, R45.2, SW_EMCON.2, SW_LIGHT.4, SW_MAIN.4, SW_SOS.2, SW_TEST.2, SW_TEST.4, SW_ZERO.2, TP8.1, U1.3 (A2), U1.12 (VSS), U1.21 (A0), U2.3 (A2), U2.12 (VSS), U3.19 (TESTEN), U3.57 (GND), U4.4 (GND), U4.9 (GND), U5.2 (GND), U6.2 (GND), U7.2 (GND), U8.2 (GND), U9.3 (GND), U10.2 (GND), U11.2 (GND), U12.3 (GND), U_LIGHT.3 (GND), Y1.2 (G), Y1.4 (G)
GPS_A: D8.2 (A), R27.2
GPS_K: D8.1 (K), U1.11 (IO0_7)
HB1: J_PANEL.18, TP28.1, U3.13 (GPIO10)
HB2: J_PANEL.19, TP29.1, U3.14 (GPIO11)
HB3: J_PANEL.20, TP30.1, U3.15 (GPIO12)
HDMI_SEL1: J_PANEL.12, TP34.1, U3.27 (GPIO16)
HDMI_SEL2: J_PANEL.13, TP35.1, U3.28 (GPIO17)
LED_RAIL: Q1.3 (D), R21.1, R22.1, R23.1, R24.1, R25.1, R26.1, R27.1, R28.1, R29.1, R30.1, R31.1, R32.1, R33.1, R34.1, R35.1, R36.1, R40.1, R41.1, TP4.1
LED_RAIL_SW: Q1.2 (S), R15.1, R17.1, R39.1, SW_LIGHT.1, TP5.1
LED_STAT: R6.1, U3.37 (GPIO25)
LED_STAT_A: D18.2 (A), R6.2
LIGHT_DAY_n: C22.1, R12.1, SW_LIGHT.5, U1.13 (IO1_0)
LIGHT_NIGHT_n: C23.1, R13.1, SW_LIGHT.6, U1.14 (IO1_1)
LTE_A: D7.2 (A), R26.2
LTE_K: D7.1 (K), U1.10 (IO0_6)
MAINRING_A: R39.2, SW_MAIN.3
MAINSW_A: FB1.1, SW_MAIN.1
MAINSW_A2: C26.1, FB1.2, J_MAINSW.1, U10.1 (I/O1), U10.6 (I/O1)
MAINSW_B: FB2.1, SW_MAIN.2
MAINSW_B2: C26.2, FB2.2, J_MAINSW.2, U10.3 (I/O2), U10.4 (I/O2)
MCAUT_A: D2.2 (A), R22.2
MCAUT_K: D2.1 (K), U1.6 (IO0_2)
MESH_A: D6.2 (A), R25.2
MESH_K: D6.1 (K), U1.9 (IO0_5)
MSG_A: D11.2 (A), R30.2
MSG_K: D11.1 (K), U2.5 (IO0_1)
MWARN_A: D1.2 (A), R21.2
MWARN_K: D1.1 (K), U1.5 (IO0_1)
PANEL_ID: JP2.1 (A), R16.1, U1.15 (IO1_2)
PANEL_PWM: R19.1, U3.11 (GPIO8)
PIJ2_A: FB3.1, SW_PI.1, TP39.1
PIJ2_A2: C27.1, FB3.2, J_PIJ2.1, U11.1 (I/O1), U11.6 (I/O1)
PIJ2_B: FB4.1, SW_PI.2, TP40.1
PIJ2_B2: C27.2, FB4.2, J_PIJ2.2, U11.3 (I/O2), U11.4 (I/O2)
PIRING_A: R40.2, SW_PI.3
PIRING_K: SW_PI.4, U2.6 (IO0_2)
PI_KILL: J_PANEL.25, TP37.1, U3.30 (GPIO19)
PI_SHDN_REQ: J_PANEL.24, TP36.1, U3.29 (GPIO18)
PWM1: R44.1, U3.12 (GPIO9)
Q1_G: Q1.1 (G), R17.2, R18.1
Q2_D: Q2.3 (D), R18.2
Q2_G: Q2.1 (G), R19.2, R20.1
Q3_G: Q3.1 (G), R37.2, R38.1
Q4_G: Q4.1 (G), R44.2, R45.1
QSPI_D0: U3.53 (QSPI_SD0), U4.5 (QSPI_D0)
QSPI_D1: U3.55 (QSPI_SD1), U4.2 (QSPI_D1)
QSPI_D2: U3.54 (QSPI_SD2), U4.3 (QSPI_D2)
QSPI_D3: U3.51 (QSPI_SD3), U4.7 (QSPI_D3)
QSPI_SCLK: U3.52 (QSPI_SCLK), U4.6 (QSPI_SCLK)
QSPI_SS: R5.1, U3.56 (QSPI_SS_N), U4.1 (QSPI_SS)
RAIL_SENSE: R15.2, U3.38 (GPIO26_A0)
SAT_A: D5.2 (A), R24.2
SAT_K: D5.1 (K), U1.8 (IO0_4)
SCL: J_PANEL.5, R8.1, TP43.1, U1.22 (SCL), U2.22 (SCL), U3.3 (GPIO1), U7.3 (I/O2), U7.4 (I/O2), U_LIGHT.1 (SCL)
SDA: J_PANEL.4, R7.1, TP42.1, U1.23 (SDA), U2.23 (SDA), U3.2 (GPIO0), U7.1 (I/O1), U7.6 (I/O1), U_LIGHT.4 (SDA)
SHORE_A: D9.2 (A), R28.2
SHORE_INHIBIT: J_PANEL.26, TP38.1, U3.31 (GPIO20)
SHORE_K: D9.1 (K), U2.4 (IO0_0)
SLOT_EN1: J_PANEL.21, TP31.1, U3.16 (GPIO13)
SLOT_EN2: J_PANEL.22, TP32.1, U3.17 (GPIO14)
SLOT_EN3: J_PANEL.23, TP33.1, U3.18 (GPIO15)
SOSACT_A: D4.2 (A), R23.2
SOSACT_K: D4.1 (K), U1.4 (IO0_0)
SOS_SW: C19.1, R9.1, SW_SOS.1, TP44.1, U3.40 (GPIO28_A2)
SPARE1: TP13.1, U1.16 (IO1_3)
SPARE2: TP14.1, U1.17 (IO1_4)
SPARE3: TP15.1, U1.18 (IO1_5)
SPARE4: TP16.1, U1.19 (IO1_6)
SPARE5: TP17.1, U1.20 (IO1_7)
SPARE6: TP18.1, U2.14 (IO1_1)
SPARE7: TP19.1, U2.15 (IO1_2)
SPARE8: TP20.1, U2.16 (IO1_3)
SPARE9: TP21.1, U2.17 (IO1_4)
SPARE10: TP22.1, U2.18 (IO1_5)
SPARE11: TP23.1, U2.19 (IO1_6)
SPARE12: TP24.1, U2.20 (IO1_7)
SWCLK: TP1.1, U3.24 (SWCLK)
SWDIO: TP2.1, U3.25 (SWD)
TESTRING_A: R41.2, SW_TEST.3
TEST_SW: C21.1, R11.1, SW_TEST.1, TP45.1, U3.39 (GPIO27_A1)
TR_APRS: J_PANEL.7, R37.1, TP46.1, U3.35 (GPIO23), U8.1 (I/O1), U8.6 (I/O1)
TX_A: D3.2 (A), R36.2
TX_INHIBIT_n: C24.1, J_PANEL.11, R14.1, SW_EMCON.1, TP10.1, U9.2 (TX_INHIBIT_n)
TX_K: D3.1 (K), D17.2 (A), Q3.3 (D)
TX_LAMPTEST: D17.1 (K), U2.13 (IO1_0)
USB_DM_R: R3.1, U3.46 (USB_DM)
USB_DP_R: R2.1, U3.47 (USB_DP)
USB_PNL_N: J_PANEL.16, R3.2, U6.3 (I/O2), U6.4 (I/O2)
USB_PNL_P: J_PANEL.15, R2.2, U6.1 (I/O1), U6.6 (I/O1)
XIN: C5.1, U3.20 (XIN), Y1.1
XOUT: C6.1, R1.2, Y1.3
XOUT_R: R1.1, U3.21 (XOUT)
ZEROIZE_HW: J_PANEL.10, TP12.1, U12.4 (ZEROIZE_HW)
ZEROIZE_SW: C20.1, R10.1, SW_ZERO.1, TP41.1, U3.34 (GPIO22), U12.2 (ZEROIZE_SW)

Notes on the sheet:
PCB-C CONTROL PANEL BACKER C24
RIBBON FROM B16, 5 V, 3.3 V LDO, USB AND BUS ESD, FLAGS | RP2040 PANEL CONTROLLER, FLASH, CRYSTAL, BOOTSEL, BUS PULL-UPS
RIBBON FROM B16, 5 V, 3.3 V LDO, USB AND BUS ESD, FLAGS
RP2040 PANEL CONTROLLER, FLASH, CRYSTAL, BOOTSEL, BUS PULL-UPS
page 1 of 5 MeshSat field kit V2, CERN-OHL-S-2.0 PROTOTYPE, nothing built 2026-09-26
panel ribbon from B16 J_PANEL
TLV75533PDBV 3.3 V 500 mA LDO for..
RP2040 panel controller
status
BOOTSEL
p2,4,5
p3,5
p2,5
p2,3,4
p3,4
p4,5
RP2040 PANEL CONTROLLER, FLASH, CRYSTAL, BOOTSEL, BUS PULL-UPS | EXPANDERS 0x22 / 0x23, MODE INPUTS, EMCON AND ZEROIZE BUFFERS, STRAPS | LED RAIL, INDICATORS, TX LAMP
RP2040 PANEL CONTROLLER, FLASH, CRYSTAL, BOOTSEL, BUS PULL-UPS (continued)
EXPANDERS 0x22 / 0x23, MODE INPUTS, EMCON AND ZEROIZE BUFFERS, STRAPS
LED RAIL, INDICATORS, TX LAMP, SWITCHES AND LEADS
page 2 of 5 MeshSat field kit V2, CERN-OHL-S-2.0 PROTOTYPE, nothing built 2026-09-26
W25Q16JVUXIQ 16 Mbit QSPI flash
12 MHz ABM8-272-T3
PCA9555PW 0x22
PANEL_ID strap
PCA9555PW 0x23
74LVC1G17 Schmitt-trigger non-inve..
LIGHTING DAY/NIGHT/BLACKOUT toggle..
p1,4,5
p1,5
LED RAIL, INDICATORS, TX LAMP, SWITCHES AND LEADS (continued)
page 3 of 5 MeshSat field kit V2, CERN-OHL-S-2.0 PROTOTYPE, nothing built 2026-09-26
3 mm MWARN red
3 mm MCAUT amber
3 mm SOSACT red
3 mm SAT green
3 mm MESH green
3 mm LTE green
3 mm GPS green
3 mm SHORE green
3 mm CHG white
3 mm MSG white
3 mm BAT1 amber
3 mm BAT2 green
3 mm BAT3 green
3 mm BAT4 green
3 mm BAT5 green
3 mm TX red
MAIN PWR 19 mm momentary
PI 16 mm recessed momentary
p1,2,4
p1,4
LED RAIL, INDICATORS, TX LAMP, SWITCHES AND LEADS | E-PAPER ZIF AND THE PDi BOOST, SOUNDER, LIGHT SENSOR, CAMERA MOUNT | STANDOFF SCREWS (GND BOND), TEST POINTS, THE
E-PAPER ZIF AND THE PDi BOOST, SOUNDER, LIGHT SENSOR, CAMERA MOUNT
STANDOFF SCREWS (GND BOND), TEST POINTS, THE REST
page 4 of 5 MeshSat field kit V2, CERN-OHL-S-2.0 PROTOTYPE, nothing built 2026-09-26
TEST/ACK 16 mm momentary
SOS locking toggle
EMCON locking toggle
ZEROIZE locking toggle
MAIN button lead to A22 J_MAINSW
PI button lead
Hirose FH34SRJ-24S-0.5SH ZIF for t..
SS2040FL
AO3401A P-FET
Si2300DS-T1-GE3 N-FET
10uH
IP67 panel-mount sounder
Vishay VEML7700 ambient light sensor
M2 screw of the USB camera module
U-174/U headset jack 1
U-174/U headset jack 2
p1,2,5
p1,3
p1,2,3
STANDOFF SCREWS (GND BOND), TEST POINTS, THE REST (continued)
page 5 of 5 MeshSat field kit V2, CERN-OHL-S-2.0 PROTOTYPE, nothing built 2026-09-26
M3 x 6 into the face plate's self-..
p1,2
