meshsat/meshsat-fieldkit/v2/release/review-packets/D-D12-1f614233/native/pcb-d-aprs.kicad_sch

## KiCad design v2/release/review-packets/D-D12-1f614233/native/pcb-d-aprs.kicad_sch (2026-09-26)

Schematic: pcb-d-aprs.kicad_sch

Parts:
C1, C2, C5: 47u 6.3V X5R 1210; C_1210_3225Metric
C3, C9, C17, C24, C25, C33, C40: 10u; C_0805_2012Metric
C4, C6, C11, C15, C16, C39, C49, C50, C51, C52, C53, C54, C55, C56, C57, C63: 100n; C_0603_1608Metric
C7, C8, C12, C18, C19, C20, C21, C22, C23, C28, C29, C30, C31, C32, C34, C35, C36, C37, C38, C41, C42, C46, C47, C48: 1u; C_0603_1608Metric
C10: 4.7u; C_0805_2012Metric
C13, C14, C26, C27: 27p NP0; C_0402_1005Metric
C43: 100p NP0; C_0402_1005Metric
C44, C45: 1n NP0; C_0402_1005Metric
C58, C60: 22p 500V NP0 1206; C_1206_3216Metric
C59: 39p 500V NP0 1206; C_1206_3216Metric
C61, C64, C65: 1u; C_0603_1608Metric; LCSC C15849
C62: 2.2u 16V X5R; C_0603_1608Metric; LCSC C23630
D1: SMBJ6.0A (6.0 V standoff on the 5.09 V mezzanine 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; D_SMB; LCSC C83270
D2: 1N4148W coil flyback; D_SOD-123
D9, D11, D12, D14: PESD5V0S1BA bidirectional ESD clamp at the jack: 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; D_SOD-323; LCSC C19224
D10, D13: PESD12VL1BA bidirectional ESD clamp at the jack: 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; D_SOD-323; LCSC C38558
FB1: 600R 2A ferrite (the exciter's 1 A transmit pulse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; L_0805_2012Metric
JP1: electret bias headset 1 (close for an electret mi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; SolderJumper-2_P1.3mm_Open_RoundedPad1.0x1.5mm
JP2: electret bias headset 2; SolderJumper-2_P1.3mm_Open_RoundedPad1.0x1.5mm
J_ANT: SMA jack: antenna pigtail to A22's VHF jack J_RF1; SMA_Amphenol_132134_Vertical; LCSC C3174425
J_HARN1: A22 mezzanine harness J_MEZZ1 (IDC 2x8): USB pair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; IDC-Header_2x08_P2.54mm_Vertical_NarrowPad
J_HS1: JST-PH 1x5 socket: headset 1, SPK GND MIC GND PTT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; JST_PH_B5B-PH-K_1x05_P2.00mm_Vertical; LCSC C157993
J_HS2: JST-PH 1x5 socket: headset 2, SPK GND MIC GND PTT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; JST_PH_B5B-PH-K_1x05_P2.00mm_Vertical; LCSC C157993
J_PAIN: U.FL socket: PA drive (coax to the RA30H1317M1 in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; U.FL_Hirose_U.FL-R-SMT-1_Vertical; LCSC C88373
J_PAOUT: SMA jack: PA output (coax from the RA30H1317M1 ou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; SMA_Amphenol_132134_Vertical; LCSC C3174425
J_PWR1: JST-VH socket, 10 A: 5 V from A22 J_MEZZ_PWR1 (be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; JST_VH_B2P-VH_1x02_P3.96mm_Vertical; LCSC C274411
J_USB3: JST-PH 1x4 socket: spare hub port 3, 5V D- D+ GND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; JST_PH_B4B-PH-K_1x04_P2.00mm_Vertical; LCSC C131334
J_VGG: JST-PH 1x2 socket: PA gate bias, VGG GND (the lea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; JST_PH_B2B-PH-K_1x02_P2.00mm_Vertical; LCSC C5251182
K1: Omron G6K-2F-Y 5 VDC DPDT signal relay, T/R; Relay_DPDT_Omron_G6K-2F-Y
L1: 68nH 0805 (LPF, 145 MHz 5th order; values to be v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; L_0805_2012Metric
L2: 68nH 0805 (LPF); L_0805_2012Metric
LED1: green power; LED_0603_1608Metric; LCSC C12624
LED2: amber record; LED_0603_1608Metric; LCSC C2287
LED3: green playback; LED_0603_1608Metric; LCSC C12624
LED4: red transmit; LED_0603_1608Metric; LCSC C2286
LED5: amber PA keyed; LED_0603_1608Metric; LCSC C2287
LED6: green receive (AUDIO_ON low); LED_0603_1608Metric; LCSC C12624
Q1: 2N7002 PA_EN -> H/L low (never tie H/L high); SOT-23; LCSC C8545
Q2: 2N7002 relay coil; SOT-23; LCSC C8545
Q3, Q4, Q5, Q6, Q7, Q8, Q9: 2N7002; SOT-23; LCSC C8545
R1, R43, R44, R51: 2.2k; R_0603_1608Metric
R2, R3, R53: 100k; R_0603_1608Metric
R4, R29, R30, R49, R50, R52: 1k; R_0603_1608Metric
R5, R9, R10, R31, R32, R35, R36, R37, R38, R39, R45, R46, R47, R66, R67, R68, R69, R70, R71, R72, R73, R74, R75, R76, R77, R78, R79: 10k; R_0603_1608Metric
R6, R7, R12, R13, R16, R17, R20, R21: 22; R_0603_1608Metric
R8, R28: 1.5k; R_0603_1608Metric
R11: 1.0k; R_0603_1608Metric
R14, R15, R18, R19, R22, R23, R24, R25: 15k; R_0603_1608Metric
R26, R27: 33; R_0603_1608Metric
R33: 470R; R_0603_1608Metric; LCSC C23179
R34, R40, R41: 4.7k; R_0603_1608Metric
R42: 220k; R_0603_1608Metric
R48: 100; R_0603_1608Metric
R54, R56: 27 1% 2010; R_2010_5025Metric
R55: 36 1% 2010; R_2010_5025Metric
R80: 56.2k 0.1% 25ppm; R_0603_1608Metric; LCSC C705784
R81: 10.7k 0.1% 25ppm; R_0603_1608Metric; LCSC C861078
R82: 71.5k 1%; R_0603_1608Metric; LCSC C23103
R83: 10.0k 1%; R_0603_1608Metric; LCSC C25804
TP1: AF_OUT; TestPoint_Pad_D1.5mm
TP2: MIC_SUM; TestPoint_Pad_D1.5mm
TP3: KEY; TestPoint_Pad_D1.5mm
TP4: PA_KEY; TestPoint_Pad_D1.5mm
TP5: +3V3_D8; TestPoint_Pad_D1.5mm
TP6: +5V_D8; TestPoint_Pad_D1.5mm
TP7: VGG_SW; TestPoint_Pad_D1.5mm
TP8: RX_MIX; TestPoint_Pad_D1.5mm
TP9: ZEROIZE_HW; TestPoint_Pad_D1.5mm
TP10: AB_SPARE; TestPoint_Pad_D1.5mm
TP11: SA_TXD; TestPoint_Pad_D1.5mm
TP12: SA_RXD; TestPoint_Pad_D1.5mm
TP13: PTT_SW_n; TestPoint_Pad_D1.5mm
TP14: SA_PD; TestPoint_Pad_D1.5mm
TP15: TX_INHIBIT_n; TestPoint_Pad_D1.5mm
TP16: PA_EN; TestPoint_Pad_D1.5mm
TP17: EXP_SPARE1; TestPoint_Pad_D1.5mm
TP18: EXP_SPARE2; TestPoint_Pad_D1.5mm
TP19: EXP_SPARE3; TestPoint_Pad_D1.5mm
TP20: EXP_SPARE4; TestPoint_Pad_D1.5mm
TP21: EXP_SPARE5; TestPoint_Pad_D1.5mm
TP22: EXP_SPARE6; TestPoint_Pad_D1.5mm
TP23: EXP_SPARE7; TestPoint_Pad_D1.5mm
TP24: EXP_SPARE8; TestPoint_Pad_D1.5mm
TP25: +3V4_HUB; TestPoint_Pad_D1.5mm
U1: TLV75533PDBV 3.3 V 500 mA LDO (1 IN 2 GND 3 EN 4 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; SOT-23-5
U2: NiceRF SA868 VHF 2 W exciter, bench-fitted (caste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; NiceRF_SA868
U3: CP2102N-A02-GQFN28 USB-UART bridge (SAU); QFN-28-1EP_5x5mm_P0.5mm_EP3.35x3.35mm; LCSC C964632
U4: TUSB2046IBVFR four-port USB 2.0 full-speed hub (T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; LQFP-32_7x7mm_P0.8mm; LCSC C702369
U5: USBLC6-2SC6; SOT-23-6; LCSC C7519
U6: TI PCM2912A USB audio codec (TQFP-32): mono input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; TQFP-32_7x7mm_P0.8mm
U7: TI TPA6132A2 headphone amplifier (QFN-16), receiv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; QFN-16-1EP_3x3mm_P0.5mm_EP1.75x1.75mm
U8: TLV9062IDGK dual op amp (1 OUT1 2 IN1- 3 IN1+ 4 V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; VSSOP-8_3x3mm_P0.65mm
U9: 74LVC1G08 AND (1 A 2 B 3 GND 4 Y 5 VCC): both hea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; SOT-23-5
U10: 74LVC1G08 AND: headsets AND software PTT (RTS); SOT-23-5
U11: 74LVC1G04 inverter (2 A 4 Y): PTT_ANY; SOT-23-5
U12: 74LVC1G08 AND: KEY = PTT_ANY AND TX_INHIBIT_n (th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; SOT-23-5
U13: 74LVC1G04 inverter: KEY -> SA868 PTT (low = trans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; SOT-23-5
U14: 74LVC1G08 AND: PA_KEY = KEY AND PA_EN (A22's PA r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; SOT-23-5
U15: TLV75801PDRVR adjustable LDO, PA gate bias VGG 4.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; WSON-6-1EP_2x2mm_P0.65mm_EP1x1.6mm; LCSC C2876308
U16: PCA9555PW 0x26: COS, PTT states, KEY, PA_KEY in; 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; TSSOP-24_4.4x7.8mm_P0.65mm
U17: TLV75801PDBVR adjustable LDO, +3V4_HUB 3.44 V for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; SOT-23-5; LCSC C2877852
Y1: 6 MHz HC-49S-SMD passive (CL 20 pF, 80 Ohm; C1 = 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; Crystal_SMD_HC49-SD; LCSC C252308
Y2: 6 MHz HC-49S-SMD passive (codec clock, CL 20 pF; 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; Crystal_SMD_HC49-SD; LCSC C252308

Connections:
+3V3: C63.1, J_HARN1.13, R67.2, R69.2, R71.2, R73.2, R75.2, R77.2, R79.2, U16.2 (A1), U16.3 (A2), U16.24 (VDD)
+3V3_D8: C8.1, C9.1, C51.1, C52.1, C53.1, C54.1, C55.1, C56.1, Q3.1 (G), Q4.1 (G), Q5.1 (G), Q6.1 (G), Q7.1 (G), Q8.1 (G), Q9.1 (G), R1.1, R5.2, R29.1, R30.1, R51.1, R66.2, R68.2, R70.2, R72.2, R74.2, R76.2, R78.2, TP5.1, U1.5 (+3V3_D8), U7.6 (G0), U9.5 (+3V3_D8), U10.5 (+3V3_D8), U11.5 (+3V3_D8), U12.5 (+3V3_D8), U13.5 (+3V3_D8), U14.5 (+3V3_D8)
+3V4_HUB: C15.1, C16.1, C17.1, C65.1, R8.2, R9.2, R10.2, R80.1, TP25.1, U4.3 (VCC), U4.6 (EEDATA/GANGED), U4.25 (VCC), U4.26 (EXTMEM), U17.5 (+3V4_HUB)
+5V_D8: C1.1, C2.1, C3.1, C4.1, C7.1, C18.1, C32.1, C33.1, C39.1, C57.1, C61.1, C64.1, D1.1 (K), D2.1 (K), FB1.1, J_PWR1.1, J_USB3.1, K1.1, R38.1, R43.2, R44.2, TP6.1, U1.1 (+5V_D8), U1.3 (+5V_D8), U3.7 (VREGIN), U3.8 (VBUS), U5.5 (VBUS), U6.2 (VBUS), U7.14 (VDD), U8.8 (+5V_D8), U15.6 (+5V_D8), U17.1 (+5V_D8), U17.3 (+5V_D8)
+5V_SA: C5.1, C6.1, FB1.2, U2.8 (VBAT)
AB_SPARE: J_HARN1.16, TP10.1
AF_DIV: C28.1, R31.2, R32.1
AF_OUT: R31.1, R35.1, TP1.1, U2.3 (AF_OUT)
AMP_CPN: C30.2, U7.9 (CPN)
AMP_CPP: C30.1, U7.11 (CPP)
AMP_EN: Q9.2 (S), R78.1, U7.13 (EN)
AMP_HPVDD: C31.1, U7.12 (HPVDD)
AMP_HPVSS: C29.1, U7.8 (HPVSS)
AMP_INL_N: C37.1, U7.1 (INL-)
AMP_INL_P: C35.2, U7.2 (INL+)
AMP_INR_N: C38.1, U7.4 (INR-)
AMP_INR_P: C36.2, U7.3 (INR+)
EXP_INT: J_HARN1.12, U16.1 (~INT)
EXP_SPARE1: TP17.1, U16.13 (IO1_0)
EXP_SPARE2: TP18.1, U16.14 (IO1_1)
EXP_SPARE3: TP19.1, U16.15 (IO1_2)
EXP_SPARE4: TP20.1, U16.16 (IO1_3)
EXP_SPARE5: TP21.1, U16.17 (IO1_4)
EXP_SPARE6: TP22.1, U16.18 (IO1_5)
EXP_SPARE7: TP23.1, U16.19 (IO1_6)
EXP_SPARE8: TP24.1, U16.20 (IO1_7)
GND: C1.2, C2.2, C3.2, C4.2, C5.2, C6.2, C7.2, C8.2, C9.2, C10.2, C11.2, C12.2, C13.2, C14.2, C15.2, C16.2, C17.2, C18.2, C19.2, C20.2, C21.2, C22.2, C23.2, C24.2, C25.2, C26.2, C27.2, C29.2, C31.2, C32.2, C33.2, C37.2, C38.2, C39.2, C40.2, C44.2, C45.2, C49.2, C50.2, C51.2, C52.2, C53.2, C54.2, C55.2, C56.2, C57.2, C58.2, C59.2, C60.2, C61.2, C62.2, C63.2, C64.2, C65.2, D1.2 (A), D9.1 (A1), D10.1 (A1), D11.1 (A1), D12.1 (A1), D13.1 (A1), D14.1 (A1), J_ANT.2 (Ext), J_HARN1.3, J_HARN1.4, J_HARN1.5, J_HARN1.6, J_HARN1.14, J_HS1.2, J_HS1.4, J_HS2.2, J_HS2.4, J_PAIN.2 (Ext), J_PAOUT.2 (Ext), J_PWR1.2, J_USB3.4, J_VGG.2, LED1.1 (K), LED4.1 (K), LED5.1 (K), Q1.2 (S), Q2.2 (S), R2.2, R3.2, R14.2, R15.2, R18.2, R19.2, R22.2, R23.2, R24.2, R25.2, R32.2, R34.2, R37.2, R39.2, R47.2, R53.2, R55.2, R81.2, R83.2, U1.2 (GND), U2.9 (GND), U2.10 (GND), U3.3 (GND), U3.29 (GND), U4.7 (GND), U4.8 (BUSPWR), U4.27 (TSTPLL/48MCLK), U4.28 (GND), U4.31 (TSTMODE), U5.2 (GND), U6.1 (BGND), U6.6 (DGND), U6.13 (AGND), U6.20 (HGND), U6.23 (MAMP), U6.24 (POWER), U6.25 (PGND), U6.28 (TEST0), U7.7 (G1), U7.10 (PGND), U7.15 (SGND), U7.17 (PAD), U8.4 (GND), U9.3 (GND), U10.3 (GND), U11.3 (GND), U12.3 (GND), U13.3 (GND), U14.3 (GND), U15.3 (GND), U15.7 (GND), U16.12 (VSS), U16.21 (A0), U17.2 (GND)
HS1_BIAS_R: JP1.2 (B), R43.1
HS1_MIC: C41.1, C44.1, D10.2 (A2), JP1.1 (A), J_HS1.3
HS1_MIC_AC: C41.2, R40.1
HS1_SPK: D9.2 (A2), J_HS1.1, U7.16 (OUTL)
HS2_BIAS_R: JP2.2 (B), R44.1
HS2_MIC: C42.1, C45.1, D13.2 (A2), JP2.1 (A), J_HS2.3
HS2_MIC_AC: C42.2, R41.1
HS2_SPK: D12.2 (A2), J_HS2.1, U7.5 (OUTR)
HUB_DM0: R7.2, U4.2 (DM0)
HUB_DM1: R13.1, U4.11 (DM1)
HUB_DM2: R17.1, U4.15 (DM2)
HUB_DM3: R21.1, U4.19 (DM3)
HUB_DM4: R25.1, U4.23 (DM4)
HUB_DP0: R6.2, R8.1, U4.1 (DP0)
HUB_DP1: R12.1, U4.12 (DP1)
HUB_DP2: R16.1, U4.16 (DP2)
HUB_DP3: R20.1, U4.20 (DP3)
HUB_DP4: R24.1, U4.24 (DP4)
HUB_FB: R80.2, R81.1, U17.4 (HUB_FB)
HUB_OVRCUR_n: R9.1, U4.10 (OVRCUR1_n), U4.14 (OVRCUR2_n), U4.18 (OVRCUR3_n), U4.22 (OVRCUR4_n)
HUB_RST_n: C12.1, R10.1, U4.4 (RESET_n)
HUB_XTAL1: C13.1, U4.30 (XTAL1), Y1.1
HUB_XTAL2: R11.2, U4.29 (XTAL2)
HUB_XTAL2R: C14.1, R11.1, Y1.2
KEY: Q6.2 (S), R48.1, R49.1, R72.1, TP3.1, U12.4 (KEY), U13.2 (KEY), U14.1 (KEY)
LED_PA_A: LED5.2 (A), R50.2
LED_PLAY_A: LED3.2 (A), R30.2
LED_PLAY_K: LED3.1 (K), U6.32 (PLAY)
LED_PWR_A: LED1.2 (A), R1.2
LED_REC_A: LED2.2 (A), R29.2
LED_REC_K: LED2.1 (K), U6.31 (REC)
LED_RX_A: LED6.2 (A), R51.2
LED_TX_A: LED4.2 (A), R49.2
MICAMP_AC: C46.2, R45.1
MICAMP_IN_N: C43.2, R40.2, R41.2, R42.2, U8.2 (MICAMP_IN_N)
MICAMP_OUT: C43.1, C46.1, R42.1, U8.1 (MICAMP_OUT)
MIC_IN: C48.2, U2.18 (MIC_IN)
MIC_SUM: C48.1, R45.2, R46.2, R47.1, TP2.1
MMUTE: R33.2, R34.1, U6.30 (MMUTE)
OPB_OUT: U8.6 (OPB_OUT), U8.7 (OPB_OUT)
PA_EN: J_HARN1.9, Q1.1 (G), R3.1, TP16.1, U14.2 (PA_EN)
PA_KEY: Q7.2 (S), R50.1, R52.1, R74.1, TP4.1, U14.4 (PA_KEY), U15.4 (PA_KEY)
PCM_L_AC: C34.2, R36.1
PCM_R_AC: C47.2, R46.1
PCM_VCCA: C20.1, U6.15 (VCCA)
PCM_VCCL: C21.1, U6.19 (VCCL)
PCM_VCCP: C23.1, U6.26 (VCCP)
PCM_VCCR: C22.1, U6.21 (VCCR)
PCM_VCOM1: C24.1, U6.11 (VCOM1)
PCM_VCOM2: C25.1, U6.12 (VCOM2)
PCM_VDD: C19.1, R28.2, U6.5 (VDD), U6.27 (TEST1)
PCM_VIN: C28.2, U6.16 (VIN)
PCM_VOUTL: C34.1, U6.18 (VOUTL)
PCM_VOUTR: C47.1, U6.22 (VOUTR)
PCM_XTI: C26.1, U6.8 (XTI), Y2.1
PCM_XTO: C27.1, U6.7 (XTO), Y2.2
PTT_ANY: U11.4 (PTT_ANY), U12.1 (PTT_ANY)
PTT_ANY_n: U10.4 (PTT_ANY_n), U11.2 (PTT_ANY_n)
PTT_HS1_n: C49.1, D11.2 (A2), J_HS1.5, Q4.2 (S), R68.1, U9.1 (PTT_HS1_n)
PTT_HS2_n: C50.1, D14.2 (A2), J_HS2.5, Q5.2 (S), R70.1, U9.2 (PTT_HS2_n)
PTT_HS_n: U9.4 (PTT_HS_n), U10.1 (PTT_HS_n)
PTT_SW_n: R5.1, TP13.1, U3.24 (RTS), U10.2 (PTT_SW_n)
RF_ANT: J_ANT.1 (In), K1.6
RF_DRV: J_PAIN.1 (In), R56.2
RF_LPF_M: C59.1, L1.2, L2.1
RF_LPF_OUT: C60.1, K1.5, L2.2
RF_PAD_IN: K1.4, R54.1
RF_PAD_M: R54.2, R55.1, R56.1
RF_PAOUT: C58.1, J_PAOUT.1 (In), L1.1
RF_RX: K1.2, K1.7
RF_SA: K1.3, U2.12 (ANT)
RLY_DRV: Q2.1 (G), R52.2, R53.1
RLY_K: D2.2 (A), K1.8, Q2.3 (D)
RX_MIX: C35.1, C36.1, R35.2, R36.2, R37.1, TP8.1
SAU_3V3: C10.1, C11.1, R4.2, U3.6 (VDD)
SAU_RST: R4.1, U3.9 (RSTb)
SA_AUDIO_ON_n: LED6.1 (K), Q3.2 (S), R66.1, U2.1 (AUDIO_ON_n)
SA_HL: Q1.3 (D), U2.7 (H/L)
SA_PD: Q8.2 (S), R76.1, TP14.1, U2.6 (PD)
SA_PTT_n: U2.5 (PTT_n), U13.4 (SA_PTT_n)
SA_RXD: TP12.1, U2.16 (RXD), U3.26 (TXD)
SA_TXD: TP11.1, U2.17 (TXD), U3.25 (RXD)
SCL: J_HARN1.11, U16.22 (SCL)
SDA: J_HARN1.10, U16.23 (SDA)
TR_APRS: J_HARN1.7, R48.2
TX_INHIBIT_n: J_HARN1.8, R2.1, TP15.1, U12.2 (TX_INHIBIT_n)
USB1_N: R13.2, R15.1, R27.1
USB1_NR: R27.2, U6.3 (D-)
USB1_P: R12.2, R14.1, R26.1
USB1_PR: R26.2, R28.1, U6.4 (D+)
USB2_N: R17.2, R19.1, U3.5 (D-)
USB2_P: R16.2, R18.1, U3.4 (D+)
USB3_N: J_USB3.2, R21.2, R23.1
USB3_P: J_USB3.3, R20.2, R22.1
USB_D8_N: J_HARN1.2, R7.1, U5.3 (I/O2), U5.4 (I/O2)
USB_D8_P: J_HARN1.1, R6.1, U5.1 (I/O1), U5.6 (I/O1)
VGG_FB: R82.2, R83.1, U15.2 (VGG_FB)
VGG_SW: C62.1, J_VGG.1, R82.1, TP7.1, U15.1 (VGG_SW)
VREF: C40.1, R38.2, R39.1, U8.3 (VREF), U8.5 (VREF)
X_AMP_EN: Q9.3 (D), R79.1, U16.10 (IO0_6)
X_COS_n: Q3.3 (D), R67.1, U16.4 (IO0_0)
X_KEY: Q6.3 (D), R73.1, U16.7 (IO0_3)
X_MMUTE: R33.1, U16.11 (IO0_7)
X_PA_KEY: Q7.3 (D), R75.1, U16.8 (IO0_4)
X_PTT_HS1_n: Q4.3 (D), R69.1, U16.5 (IO0_1)
X_PTT_HS2_n: Q5.3 (D), R71.1, U16.6 (IO0_2)
X_SA_PD: Q8.3 (D), R77.1, U16.9 (IO0_5)
ZEROIZE_HW: J_HARN1.15, TP9.1

Notes on the sheet:
PCB-D APRS MEZZANINE D37P
HARNESS, 5 V ENTRY, 3.3 V LDO, EXCITER SUPPLY | SA868 EXCITER, UART BRIDGE, T/R RELAY, 10 dB PAD, LPF, PA LEADS, GATE BIAS REGULATOR
HARNESS, 5 V ENTRY, 3.3 V LDO, EXCITER SUPPLY
SA868 EXCITER, UART BRIDGE, T/R RELAY, 10 dB PAD, LPF, PA LEADS, GATE BIAS REGULATOR
page 1 of 6 MeshSat field kit V2, CERN-OHL-S-2.0 PROTOTYPE, nothing built 2026-09-26
A22 mezzanine harness J_MEZZ1
JST-VH socket
SMBJ6.0A
47u 6.3V
600R 2A
TLV75533PDBV 3.3 V 500 mA LDO
NiceRF SA868 VHF 2 W exciter
2N7002 PA_EN -> H/L low
CP2102N-A02-GQFN28 USB-UART bridge
Omron G6K-2F-Y 5 VDC DPDT signal r..
27 1%
68nH 0805
U.FL socket
SMA jack
22p 500V
39p 500V
p3,5
p4,5
SA868 EXCITER, UART BRIDGE, T/R RELAY, 10 dB PAD, LPF, PA LEADS, GATE BIAS REGULATOR | USB HUB TUSB2046I AND ITS 3.44 V LDO, PORT TERMINATIONS, SPARE PORT
SA868 EXCITER, UART BRIDGE, T/R RELAY, 10 dB PAD, LPF, PA LEADS, GATE BIAS REGULATOR (continued)
USB HUB TUSB2046I AND ITS 3.44 V LDO, PORT TERMINATIONS, SPARE PORT
page 2 of 6 MeshSat field kit V2, CERN-OHL-S-2.0 PROTOTYPE, nothing built 2026-09-26
TLV75801PDRVR adjustable LDO
2.2u 16V
JST-PH 1x2 socket
TUSB2046IBVFR four-port USB 2.0 fu..
TLV75801PDBVR adjustable LDO
56.2k 0.1%
10.7k 0.1%
6 MHz HC-49S-SMD passive
JST-PH 1x4 socket
USB AUDIO CODEC PCM2912A, HEADPHONE AMPLIFIER, MIC PREAMP, HEADSET LEADS
page 3 of 6 MeshSat field kit V2, CERN-OHL-S-2.0 PROTOTYPE, nothing built 2026-09-26
TI PCM2912A USB audio codec
decoupling of U6
TI TPA6132A2 headphone amplifier
PESD5V0S1BA bidirectional ESD clam..
p1,5
USB AUDIO CODEC PCM2912A, HEADPHONE AMPLIFIER, MIC PREAMP, HEADSET LEADS | PTT AND EMCON LOGIC, PTT MIRROR, LEDS, EXPANDER 0x26 WITH LEVEL STAGES, TEST POINTS, FLAGS
USB AUDIO CODEC PCM2912A, HEADPHONE AMPLIFIER, MIC PREAMP, HEADSET LEADS (continued)
PTT AND EMCON LOGIC, PTT MIRROR, LEDS, EXPANDER 0x26 WITH LEVEL STAGES, TEST POINTS, FLAGS
page 4 of 6 MeshSat field kit V2, CERN-OHL-S-2.0 PROTOTYPE, nothing built 2026-09-26
TLV9062IDGK dual op amp
JST-PH 1x5 socket
electret bias headset 1
PESD12VL1BA bidirectional ESD clam..
74LVC1G08 AND
74LVC1G04 inverter
PTT AND EMCON LOGIC, PTT MIRROR, LEDS, EXPANDER 0x26 WITH LEVEL STAGES, TEST POINTS, FLAGS (continued)
page 5 of 6 MeshSat field kit V2, CERN-OHL-S-2.0 PROTOTYPE, nothing built 2026-09-26
PCA9555PW 0x26
green receive
p1,3
p3,4
p1,4
page 6 of 6 MeshSat field kit V2, CERN-OHL-S-2.0 PROTOTYPE, nothing built 2026-09-26
