meshsat/meshsat-fieldkit/v2/release/review-packets/E-E17-1f614233/native/pcb-e1-dock.kicad_sch

## KiCad design v2/release/review-packets/E-E17-1f614233/native/pcb-e1-dock.kicad_sch (2026-09-26)

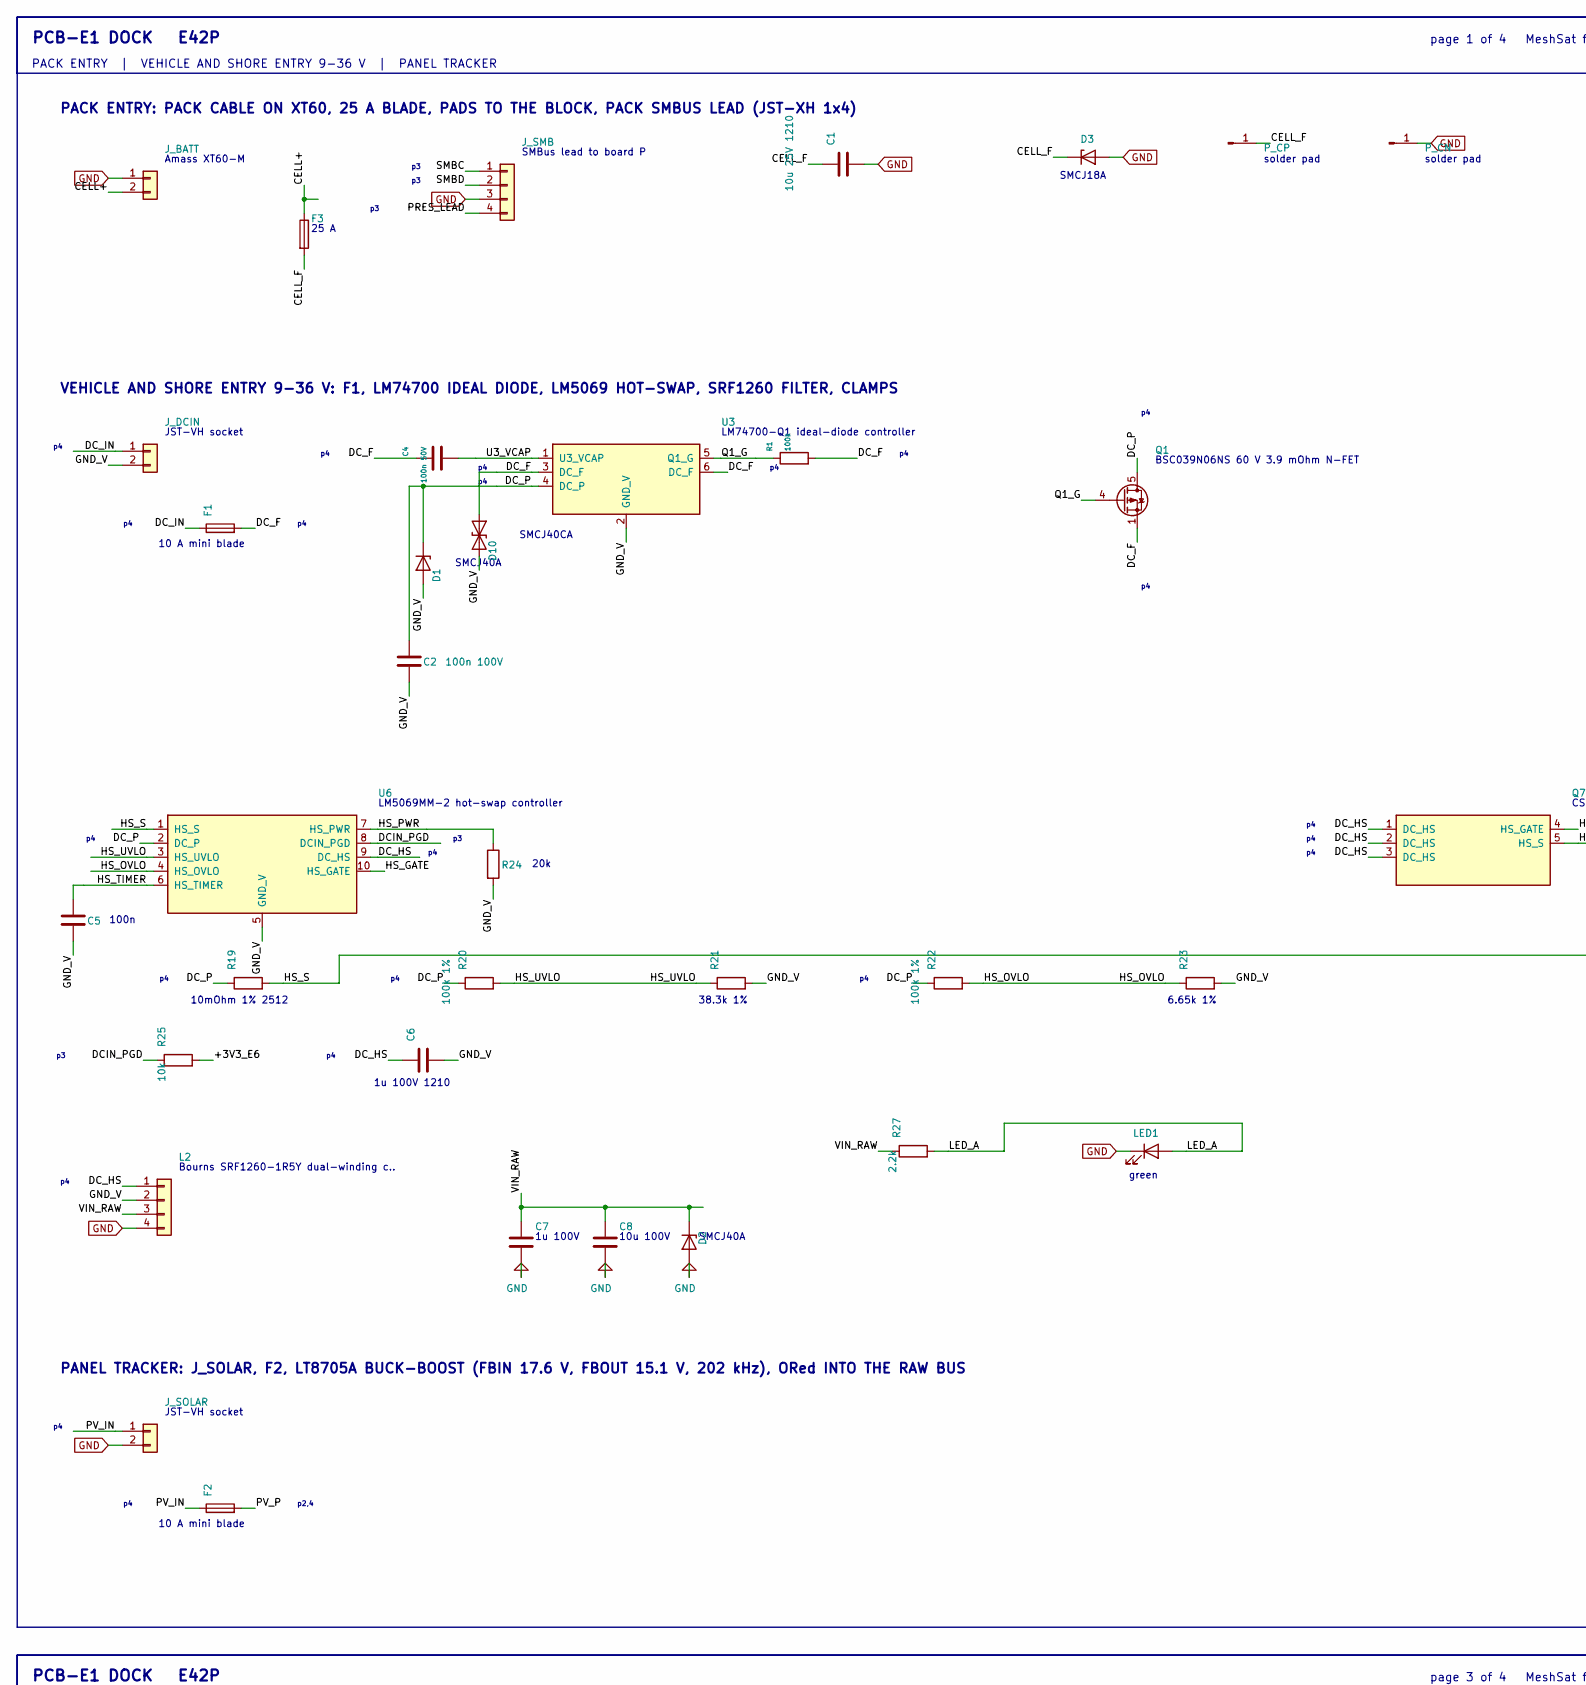
[picture p323: schematic pcb-e1-dock.kicad_sch, part in row 1, column 1]

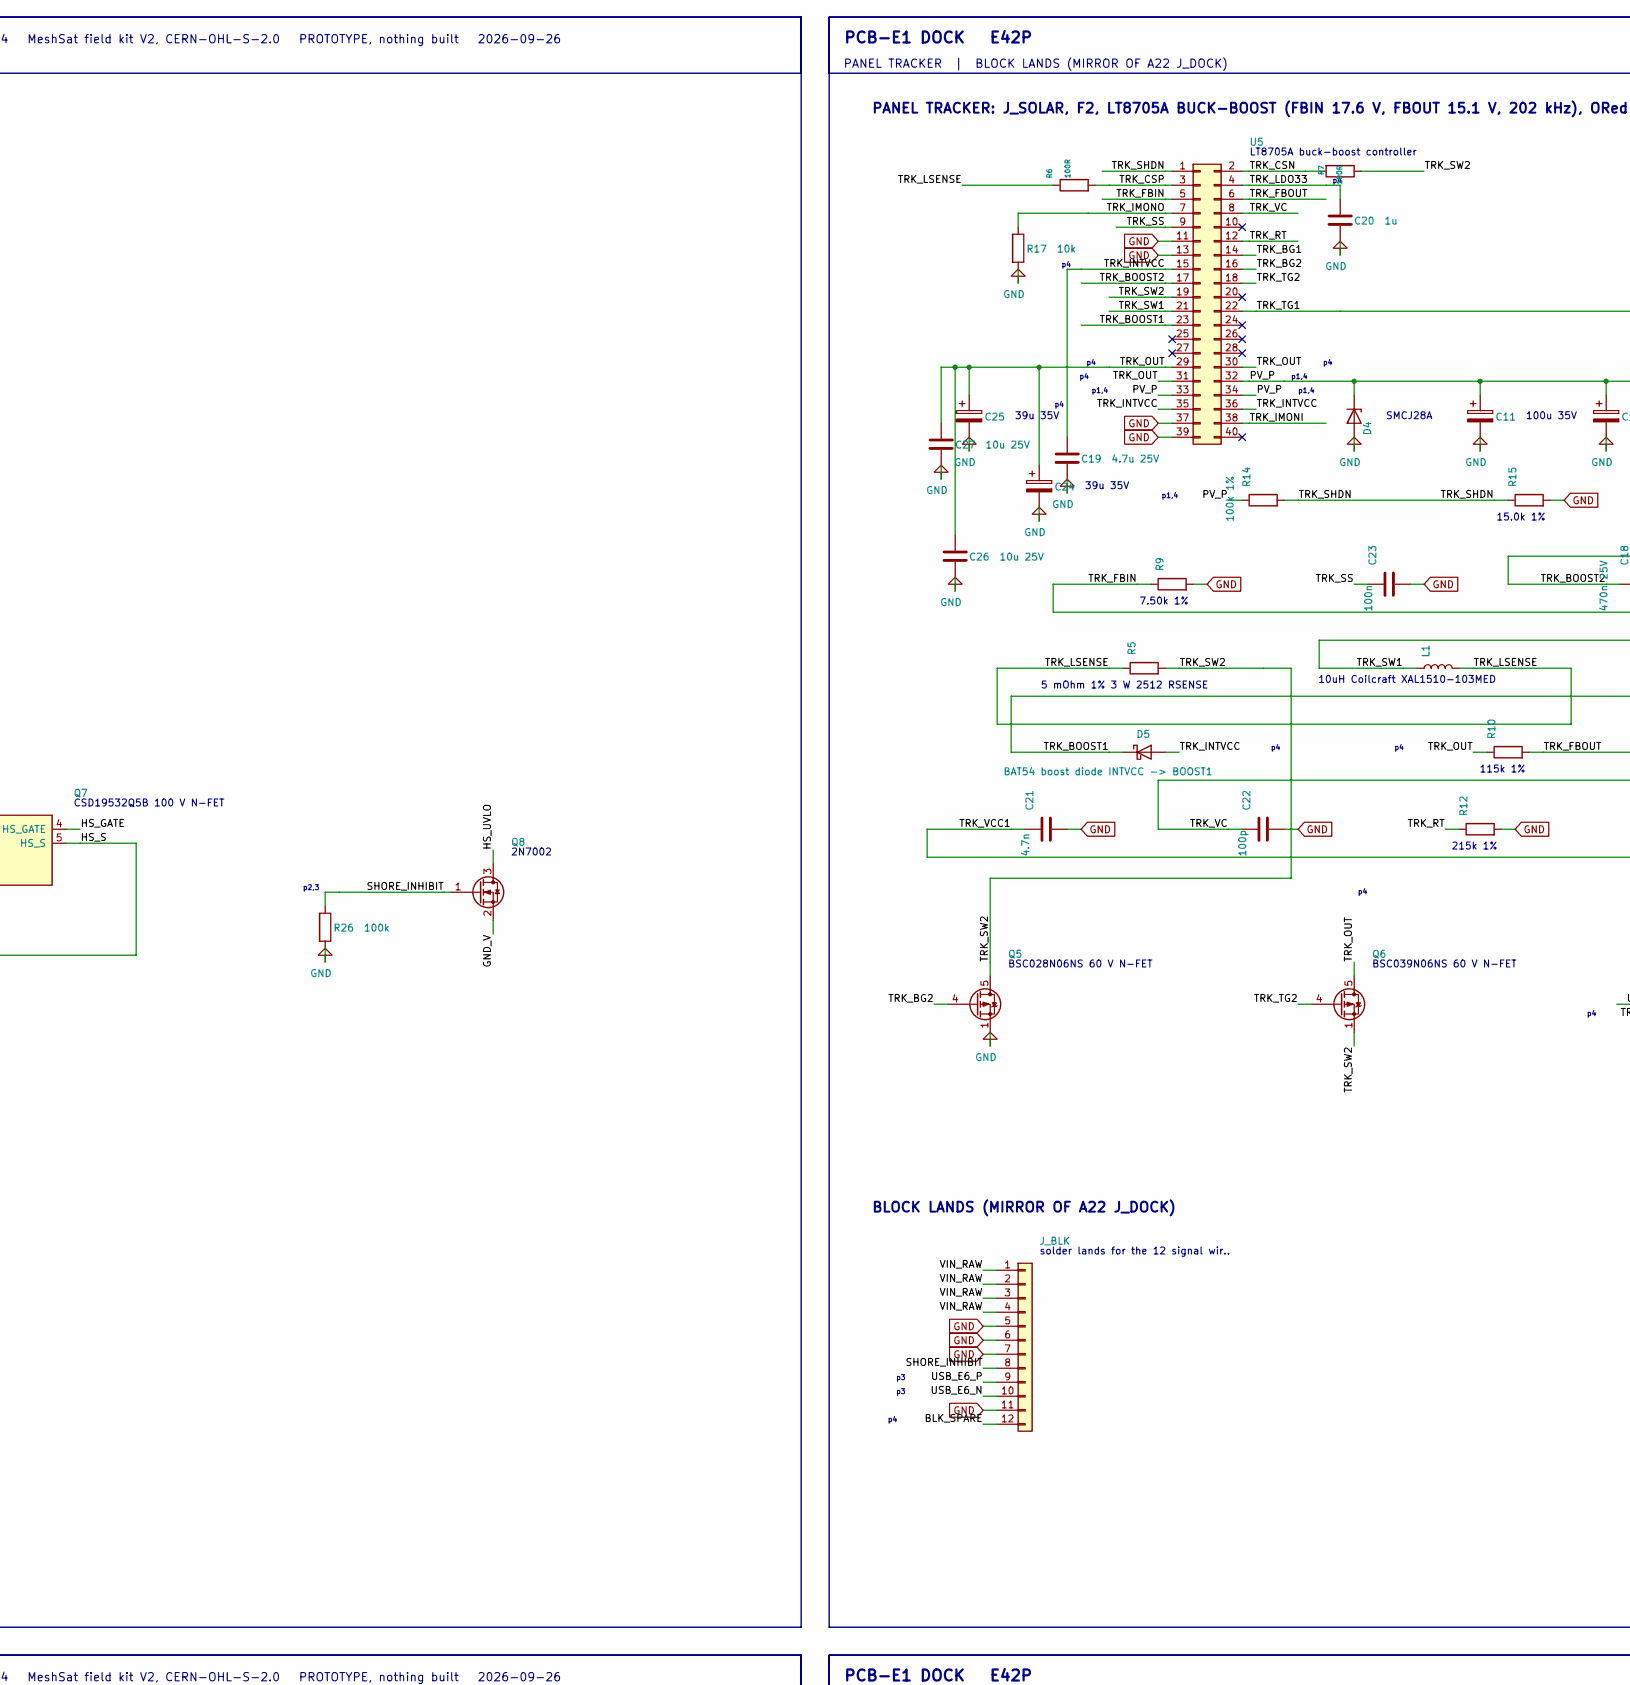
[picture p324: schematic pcb-e1-dock.kicad_sch, part in row 1, column 2]

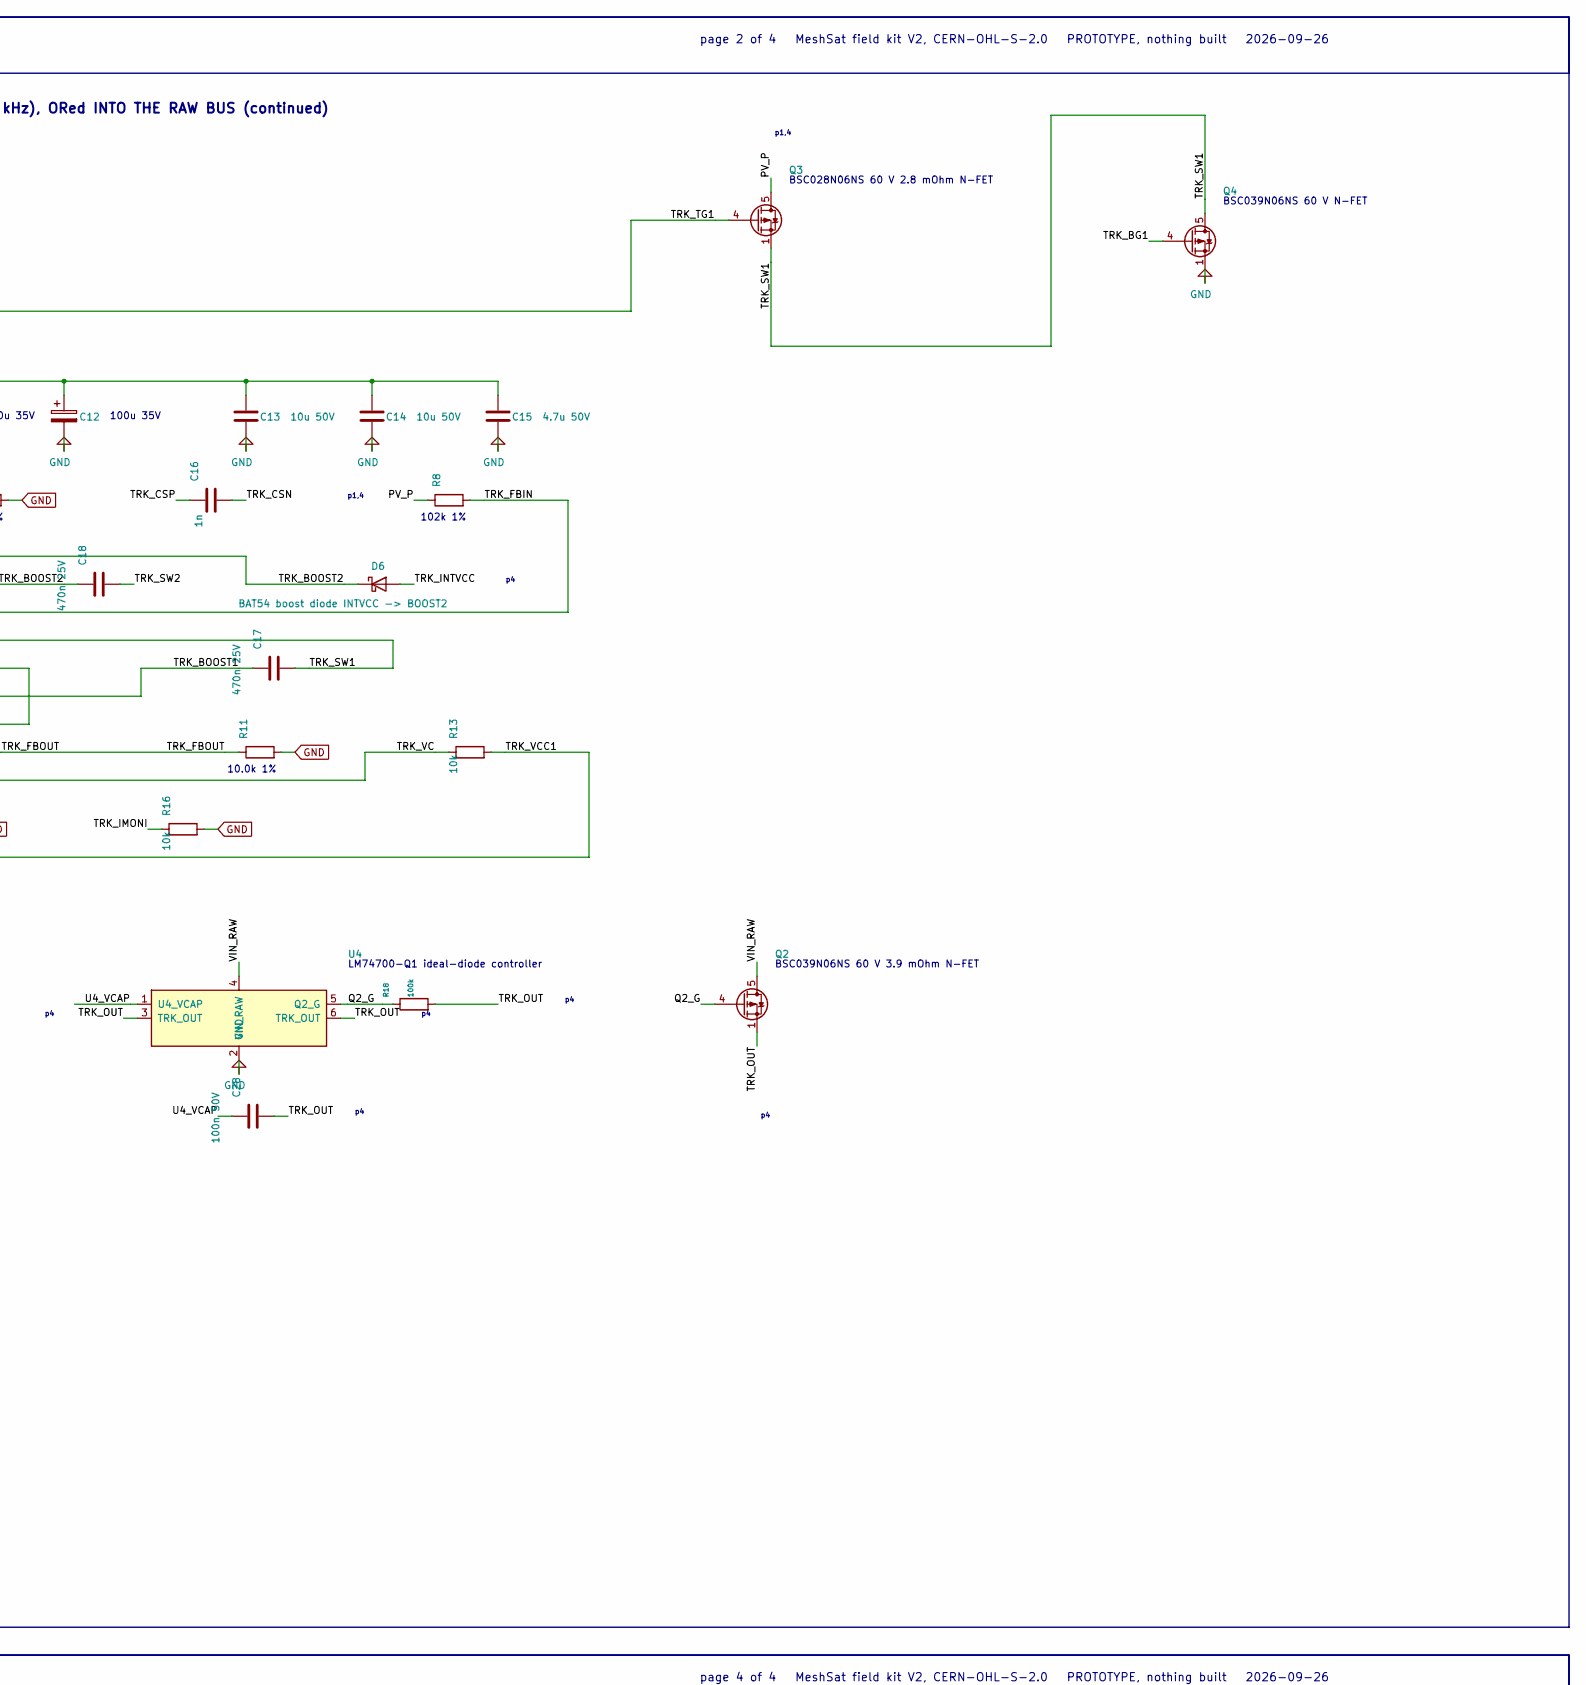
[picture p325: schematic pcb-e1-dock.kicad_sch, part in row 1, column 3]

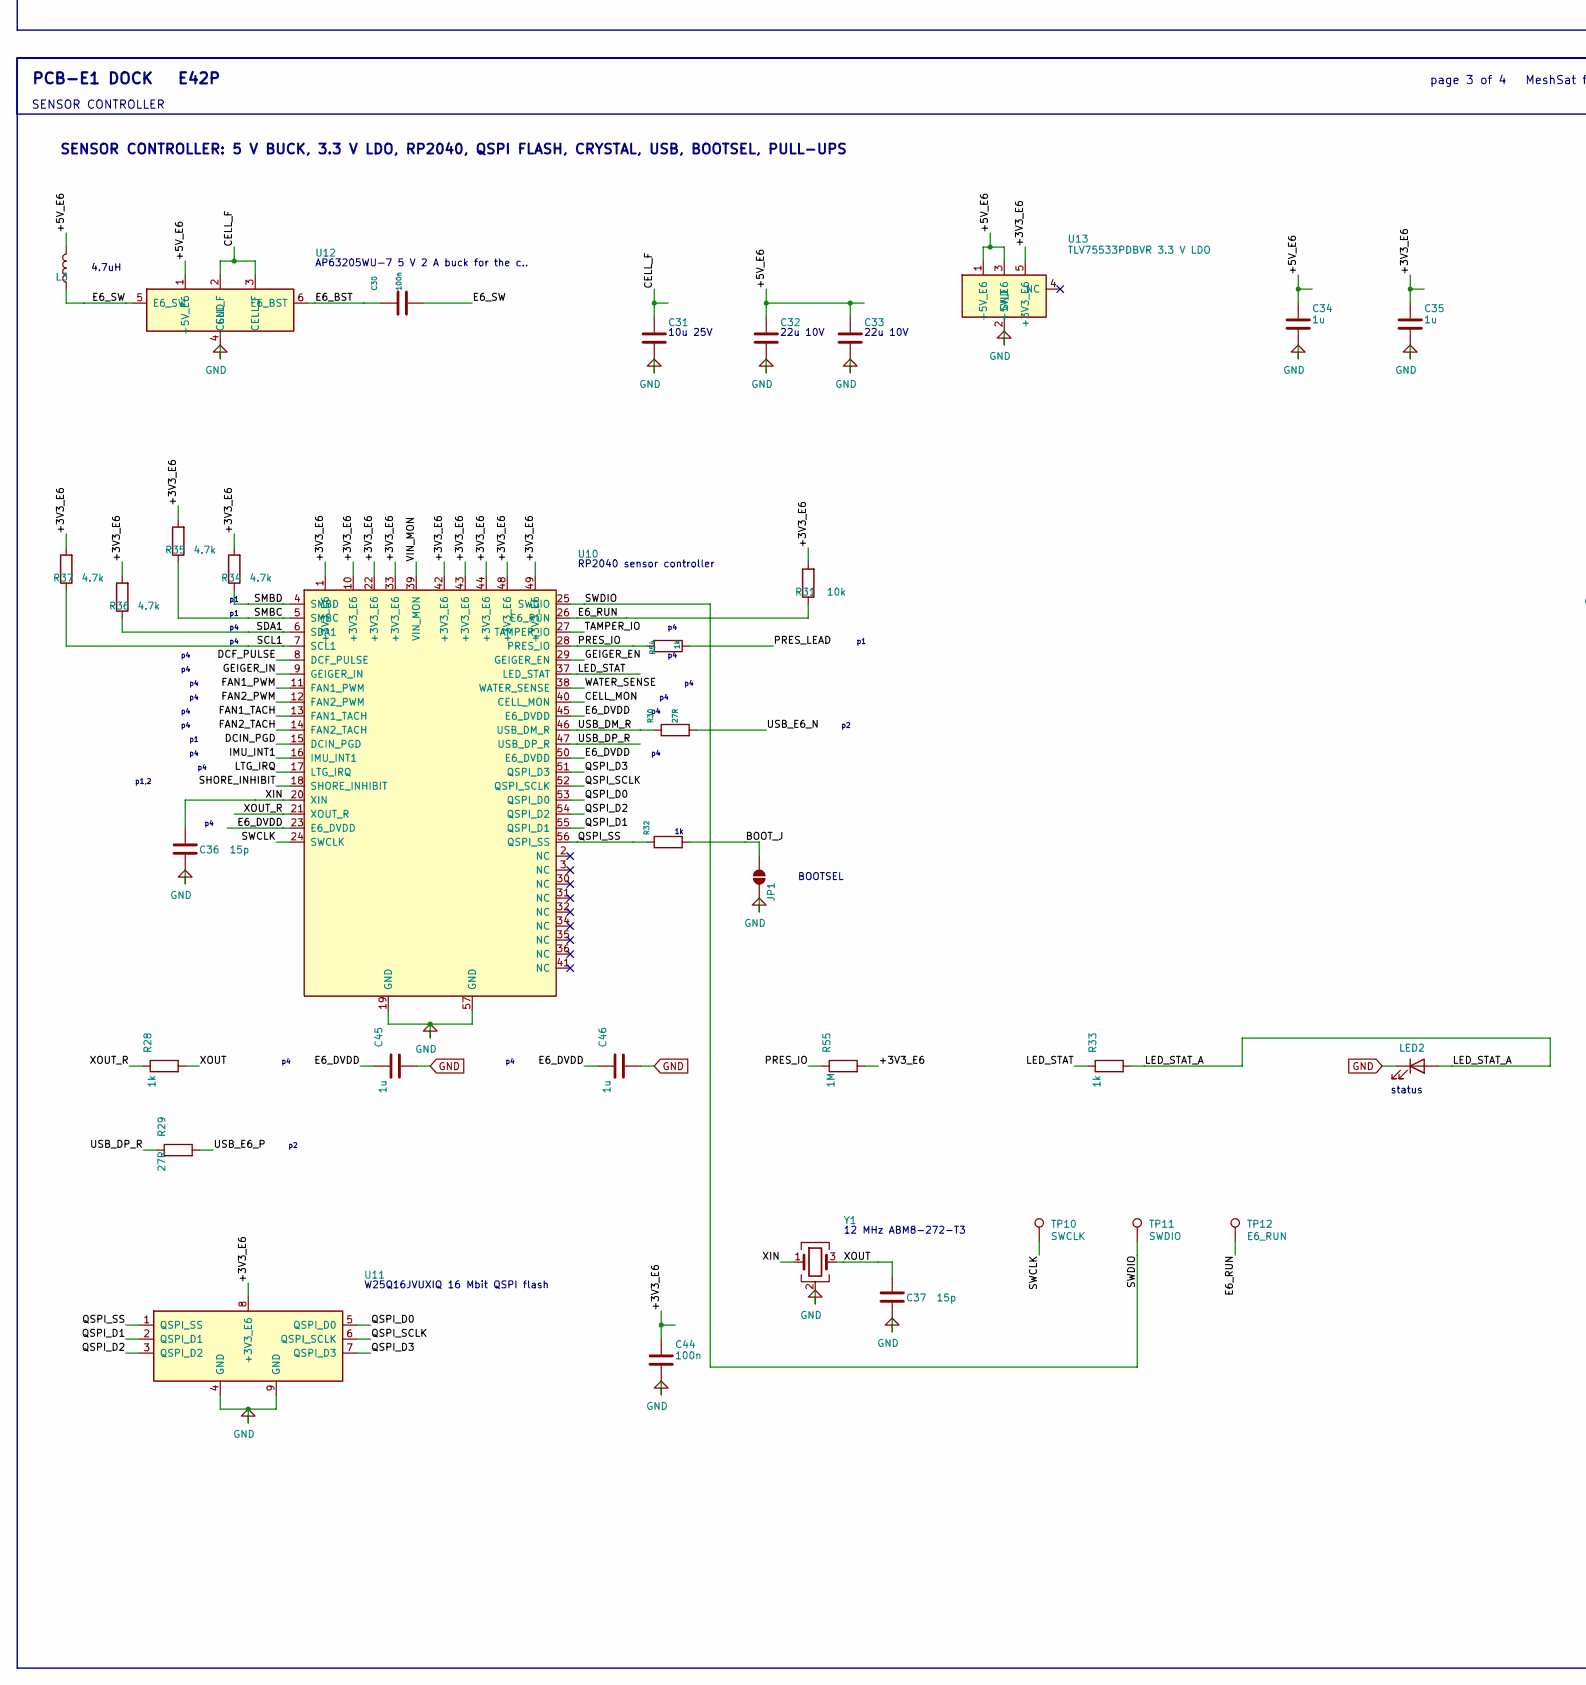
[picture p326: schematic pcb-e1-dock.kicad_sch, part in row 2, column 1]

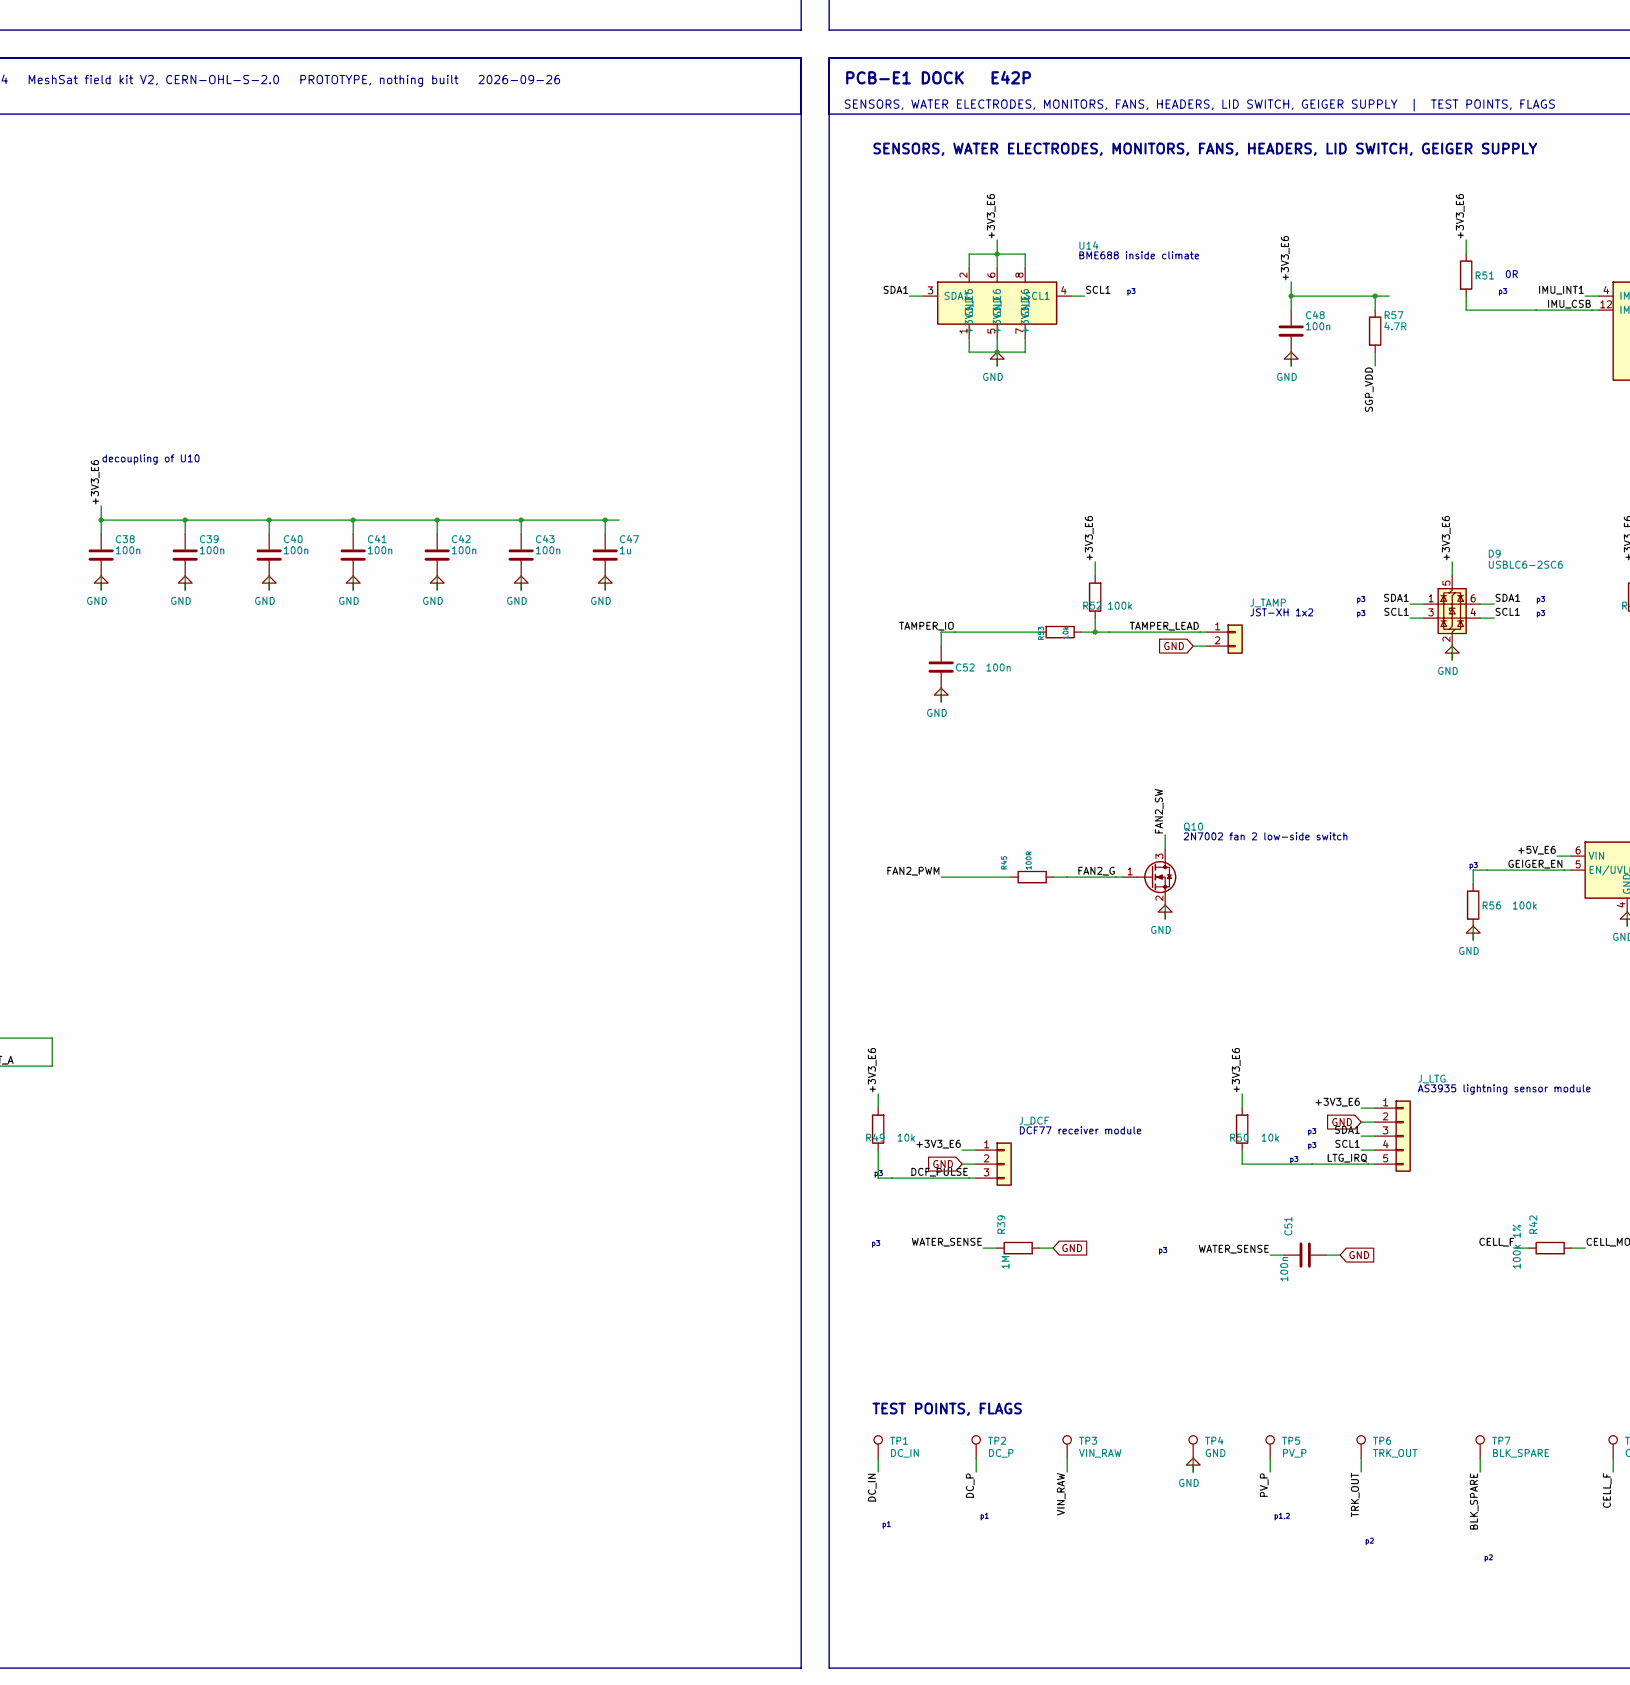
[picture p327: schematic pcb-e1-dock.kicad_sch, part in row 2, column 2]

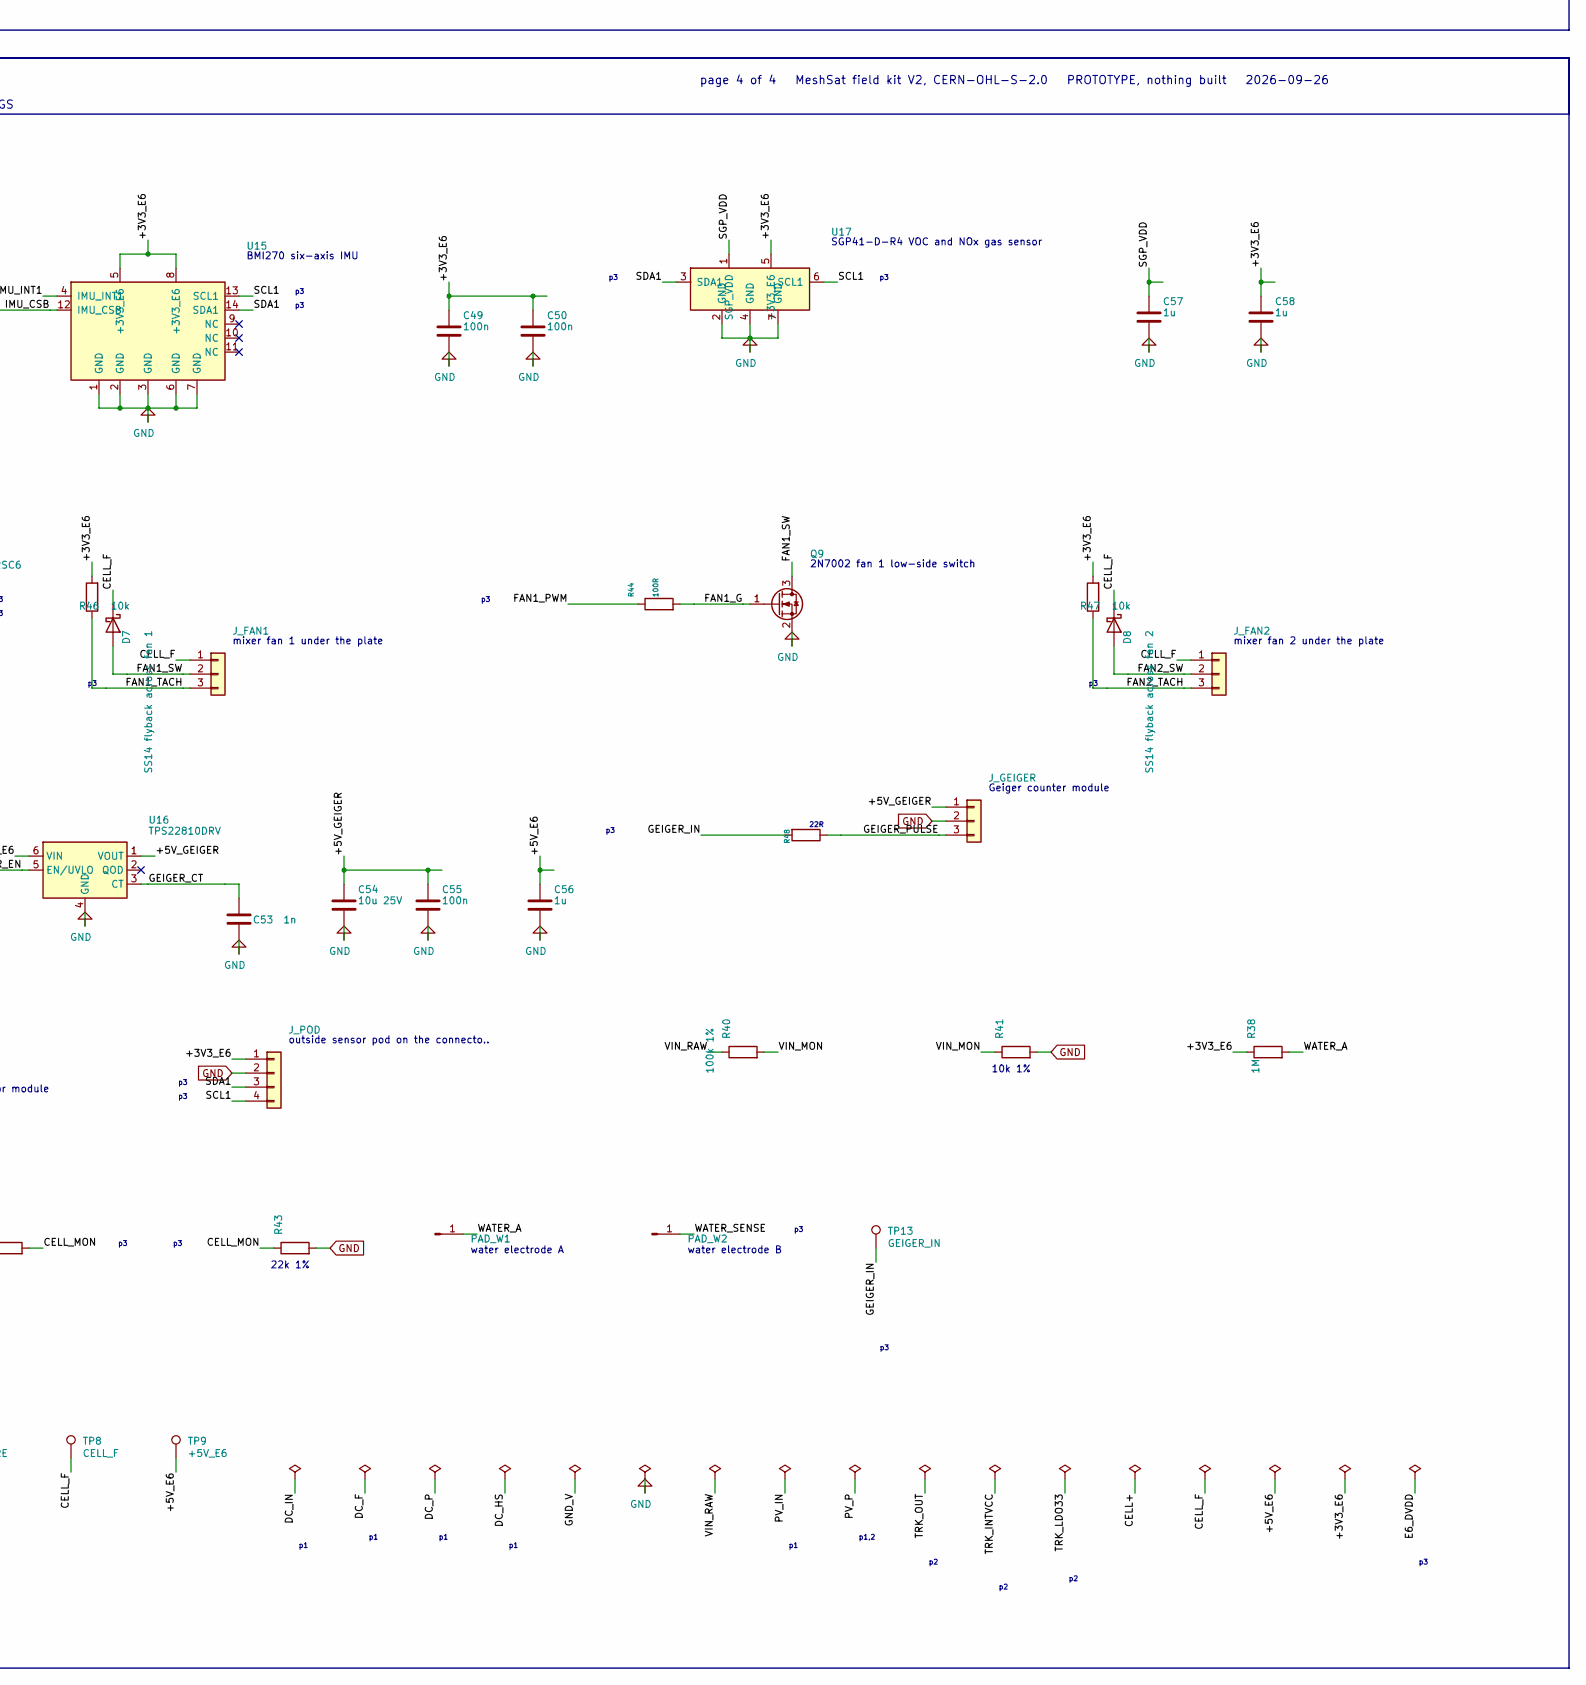
[picture p328: schematic pcb-e1-dock.kicad_sch, part in row 2, column 3]

Parts:
C1, C31: 10u 25V 1210; C_1210_3225Metric
C2: 100n 100V; C_0805_2012Metric
C4, C28: 100n 50V; C_0603_1608Metric; LCSC C14663
C5: 100n (TIMER); C_0603_1608Metric
C6: 1u 100V 1210 (X, input side); C_1210_3225Metric
C7: 1u 100V 1210 (X, bus side); C_1210_3225Metric
C8: 10u 100V X7R 1210; C_1210_3225Metric
C11, C12: 100u 35V Panasonic EEHZK1V101XP hybrid polymer (7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; CP_Elec_6.3x7.7; LCSC C454360
C13, C14: 10u 50V; C_1206_3216Metric
C15: 4.7u 50V; C_1206_3216Metric
C16: 1n; C_0603_1608Metric
C17, C18: 470n 25V; C_0603_1608Metric
C19: 4.7u 25V; C_1206_3216Metric
C20, C34, C35, C45, C46, C47: 1u; C_0603_1608Metric
C21: 4.7n; C_0603_1608Metric
C22: 100p; C_0603_1608Metric
C23, C30, C38, C39, C40, C41, C42, C43, C44, C48, C49, C50, C51: 100n; C_0603_1608Metric
C24, C25: 39u 35V Panasonic 35SVPF39M polymer (6.9 mm); CP_Elec_8x6.7; LCSC C189474
C26, C27: 10u 25V; C_1206_3216Metric
C32, C33: 22u 10V X7R 1210; C_1210_3225Metric
C36, C37: 15p; C_0603_1608Metric
C52, C55: 100n; C_0603_1608Metric; LCSC C14663
C53: 1n; C_0603_1608Metric; LCSC C1588
C54: 10u 25V; C_1206_3216Metric; LCSC C89632
C56, C57, C58: 1u; C_0603_1608Metric; LCSC C15849
D1: SMCJ40A (input surge: 40 V standoff on a line spe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; D_SMC; LCSC C224052
D2: SMCJ40A (bus clamp: 40 V standoff on the 9 to 36 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; D_SMC; LCSC C224052
D3: SMCJ18A (pack node clamp, unidirectional: cathode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; D_SMC; LCSC C374030
D4: SMCJ28A (panel surge: 28 V standoff, conducting f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; D_SMC; LCSC C224047
D5: BAT54 boost diode INTVCC -> BOOST1; D_SOD-123
D6: BAT54 boost diode INTVCC -> BOOST2; D_SOD-123
D7: SS14 flyback across fan 1; D_SMB
D8: SS14 flyback across fan 2; D_SMB
D9: USBLC6-2SC6; SOT-23-6; LCSC C7519
D10: SMCJ40CA (bidirectional, Littelfuse SMCJ40 row: 4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; D_SMC; LCSC C80273
F1: 10 A mini blade (Keystone 3568 holder): vehicle i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; Fuseholder_Blade_Mini_Keystone_3568
F2: 10 A mini blade (Keystone 3568 holder): panel inp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; Fuseholder_Blade_Mini_Keystone_3568
F3: 25 A mini blade (Keystone 3568 holder): pack to t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; Fuseholder_Blade_Mini_Keystone_3568
JP1: BOOTSEL: short while powering to enter the USB bo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; SolderJumper-2_P1.3mm_Open_RoundedPad1.0x1.5mm
J_BATT: Amass XT60-M: the BB-2590/U pack cable BTA-70762-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; AMASS_XT60-M_1x02_P7.20mm_Vertical; LCSC C98733
J_BLK: solder lands for the 12 signal wires to the block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; PogoTargets_2x6
J_DCF: DCF77 receiver module: 3.3 V, GND, pulse; PinHeader_1x03_P2.54mm_Vertical
J_DCIN: JST-VH socket, 10 A: vehicle and shore DC in 9 to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; JST_VH_B2P-VH_1x02_P3.96mm_Vertical; LCSC C274411
J_FAN1: mixer fan 1 under the plate (12 V class fan on th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; PinHeader_1x03_P2.54mm_Vertical
J_FAN2: mixer fan 2 under the plate (12 V class fan on th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; PinHeader_1x03_P2.54mm_Vertical
J_GEIGER: Geiger counter module (RadiationD-v1.1 class): 5 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; PinHeader_1x03_P2.54mm_Vertical
J_LTG: AS3935 lightning sensor module (CJMCU-3935 class)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; PinHeader_1x05_P2.54mm_Vertical
J_POD: outside sensor pod on the connector plate (M8 sea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; PinHeader_1x04_P2.54mm_Vertical
J_SMB: SMBus lead to board P, JST-XH 1x4 (B4B-XH-A), P's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; JST_XH_B4B-XH-A_1x04_P2.50mm_Vertical; LCSC C594232
J_SOLAR: JST-VH socket, 10 A: bare panel in (lead from the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; JST_VH_B2P-VH_1x02_P3.96mm_Vertical; LCSC C274411
J_TAMP: JST-XH 1x2 (B2B-XH-A): lid and tamper reed sensor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; JST_XH_B2B-XH-A_1x02_P2.50mm_Vertical; LCSC C158012
L1: 10uH Coilcraft XAL1510-103MED (Isat 26 A, 10.0 mm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; L_Coilcraft_XAL1510-103; LCSC C3911782
L2: Bourns SRF1260-1R5Y dual-winding choke, common-mo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; L_CommonModeChoke_Bourns_SRF1260
L3: 4.7uH XAL4030-472ME; L_Coilcraft_XAL4020-XXX
LED1: green: vehicle input present; LED_0603_1608Metric
LED2: status (GPIO25); LED_0603_1608Metric
PAD_W1: water electrode A (bare copper, +3.3 V through 1 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; SolderPad_8x6
PAD_W2: water electrode B (bare copper, to ADC0); SolderPad_8x6
P_CN: solder pad, 12 AWG wire to the block board return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; SolderPad_8x6
P_CP: solder pad, 12 AWG wire to the block board CELL+ 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; SolderPad_8x6
Q1, Q2: BSC039N06NS 60 V 3.9 mOhm N-FET (PG-TDSON-8: 1-3 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; TDSON-8-1; LCSC C534330
Q3: BSC028N06NS 60 V 2.8 mOhm N-FET, M1 buck top (TDS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; TDSON-8-1; LCSC C148250
Q4: BSC039N06NS 60 V N-FET, M2 buck bottom; TDSON-8-1; LCSC C534330
Q5: BSC028N06NS 60 V N-FET, M3 boost bottom; TDSON-8-1; LCSC C148250
Q6: BSC039N06NS 60 V N-FET, M4 boost top; TDSON-8-1; LCSC C534330
Q7: CSD19532Q5B 100 V N-FET (4.6 mOhm at VGS 6 V, Pow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; PowerPAK_SO-8_Single; LCSC C473333
Q8: 2N7002: SHORE_INHIBIT high pulls UVLO low = input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; SOT-23
Q9: 2N7002 fan 1 low-side switch (1 G, 2 S, 3 D); SOT-23
Q10: 2N7002 fan 2 low-side switch (1 G, 2 S, 3 D); SOT-23
R1, R18, R52, R56: 100k; R_0603_1608Metric; LCSC C25803
R5: 5 mOhm 1% 3 W 2512 RSENSE (RALEC LR2512-23R005F4); R_2512_6332Metric; LCSC C154688
R6, R7, R44, R45: 100R; R_0603_1608Metric
R8: 102k 1% (RFBIN1: panel point 17.6 V); R_0603_1608Metric
R9: 7.50k 1% (RFBIN2); R_0603_1608Metric
R10: 115k 1% (RFBOUT1: 15.1 V); R_0603_1608Metric
R11: 10.0k 1% (RFBOUT2); R_0603_1608Metric
R12: 215k 1% (RT: 202 kHz); R_0603_1608Metric
R13, R16, R17, R25, R31, R46, R47, R49, R50: 10k; R_0603_1608Metric
R14, R20, R22, R40, R42: 100k 1%; R_0603_1608Metric
R15: 15.0k 1% (SHDN: enable above about 9.5 V); R_0603_1608Metric
R19: 10mOhm 1% 2512 (hot-swap sense); R_2512_6332Metric
R21: 38.3k 1% (UVLO: 9 V); R_0603_1608Metric
R23: 6.65k 1% (OVLO: 40 V); R_0603_1608Metric
R24: 20k (PWR: power limit); R_0603_1608Metric
R26: 100k; R_0603_1608Metric
R27: 2.2k; R_0603_1608Metric; LCSC C4190
R28, R33: 1k; R_0603_1608Metric
R29, R30: 27R; R_0603_1608Metric
R32: 1k (BOOTSEL); R_0603_1608Metric
R34, R35, R36, R37: 4.7k; R_0603_1608Metric
R38, R39: 1M; R_0603_1608Metric
R41: 10k 1% (ADC1: 0.091 x bus); R_0603_1608Metric
R43: 22k 1% (ADC2: 0.18 x pack); R_0603_1608Metric
R48: 22R (pulse input series); R_0603_1608Metric
R51: 0R (CSB high: I2C mode; its own net keeps the pin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; R_0603_1608Metric
R53: 10k; R_0603_1608Metric; LCSC C25804
R54: 1k; R_0603_1608Metric; LCSC C21190
R55: 1M; R_0603_1608Metric; LCSC C22935
R57: 4.7R; R_0603_1608Metric; LCSC C23164
TP1: DC_IN; TestPoint_Pad_D1.5mm
TP2: DC_P; TestPoint_Pad_D1.5mm
TP3: VIN_RAW; TestPoint_Pad_D1.5mm
TP4: GND; TestPoint_Pad_D1.5mm
TP5: PV_P; TestPoint_Pad_D1.5mm
TP6: TRK_OUT; TestPoint_Pad_D1.5mm
TP7: BLK_SPARE; TestPoint_Pad_D1.5mm
TP8: CELL_F; TestPoint_Pad_D1.5mm
TP9: +5V_E6; TestPoint_Pad_D1.5mm
TP10: SWCLK; TestPoint_Pad_D1.5mm
TP11: SWDIO; TestPoint_Pad_D1.5mm
TP12: E6_RUN; TestPoint_Pad_D1.5mm
TP13: GEIGER_IN; TestPoint_Pad_D1.5mm
U3, U4: LM74700-Q1 ideal-diode controller: 1 VCAP 2 GND 3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; SOT-23-6; LCSC C2941042
U5: LT8705A buck-boost controller, 38-lead QFN 5x7 (p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; WQFN-38-1EP_5x7mm_P0.5mm_EP3.15x5.15mm; LCSC C674164
U6: LM5069MM-2 hot-swap controller: 9 V on, 40 V off,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; VSSOP-10_3x3mm_P0.5mm; LCSC C111822
U10: RP2040 sensor controller (USB to B16 through the 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; QFN-56-1EP_7x7mm_P0.4mm_EP3.2x3.2mm; LCSC C2040
U11: W25Q16JVUXIQ 16 Mbit QSPI flash (USON-8: 1 CS 2 D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; Winbond_USON-8-1EP_3x2mm_P0.5mm_EP0.2x1.6mm; LCSC C2843335
U12: AP63205WU-7 5 V 2 A buck for the controller, the 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; TSOT-23-6; LCSC C2071056
U13: TLV75533PDBVR 3.3 V LDO; SOT-23-5; LCSC C404027
U14: BME688 inside climate: temperature, humidity, pre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; Bosch_LGA-8_3x3mm_P0.8mm_ClockwisePinNumbering; LCSC C3664478
U15: BMI270 six-axis IMU (I2C 0x68): shock and tilt lo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; Bosch_LGA-14_3x2.5mm_P0.5mm; LCSC C2836813
U16: TPS22810DRV; WSON-6-1EP_2x2mm_P0.65mm_EP1x1.6mm
U17: SGP41-D-R4 VOC and NOx gas sensor, battery-bay ai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; Sensirion_DFN-6-1EP_2.44x2.44mm_P0.8mm_EP1.25x1.7mm; LCSC C3659325
Y1: 12 MHz ABM8-272-T3 (3225): 1 XIN, 3 XOUT, 2 and 4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; Crystal_SMD_3225-4Pin_3.2x2.5mm; LCSC C20625731

Connections:
+3V3_E6: C35.1, C38.1, C39.1, C40.1, C41.1, C42.1, C43.1, C44.1, C47.1, C48.1, C49.1, C50.1, C58.1, D9.5 (VBUS), J_DCF.1, J_LTG.1, J_POD.1, R25.2, R31.2, R34.2, R35.2, R36.2, R37.2, R38.1, R46.2, R47.2, R49.2, R50.2, R51.1, R52.2, R55.2, R57.1, U10.1 (+3V3_E6), U10.10 (+3V3_E6), U10.22 (+3V3_E6), U10.33 (+3V3_E6), U10.42 (+3V3_E6), U10.43 (+3V3_E6), U10.44 (+3V3_E6), U10.48 (+3V3_E6), U10.49 (+3V3_E6), U11.8 (+3V3_E6), U13.5 (+3V3_E6), U14.2 (+3V3_E6), U14.6 (+3V3_E6), U14.8 (+3V3_E6), U15.5 (+3V3_E6), U15.8 (+3V3_E6), U17.5 (+3V3_E6)
+5V_E6: C32.1, C33.1, C34.1, C56.1, L3.2, TP9.1, U12.1 (+5V_E6), U13.1 (+5V_E6), U13.3 (+5V_E6), U16.6 (VIN)
+5V_GEIGER: C54.1, C55.1, J_GEIGER.1, U16.1 (VOUT)
BLK_SPARE: J_BLK.12, TP7.1
BOOT_J: JP1.1 (A), R32.2
CELL+: F3.1, J_BATT.2
CELL_F: C1.1, C31.1, D3.1 (K), D7.1 (K), D8.1 (K), F3.2, J_FAN1.1, J_FAN2.1, P_CP.1, R42.1, TP8.1, U12.2 (CELL_F), U12.3 (CELL_F)
CELL_MON: R42.2, R43.1, U10.40 (CELL_MON)
DCF_PULSE: J_DCF.3, R49.1, U10.8 (DCF_PULSE)
DCIN_PGD: R25.1, U6.8 (DCIN_PGD), U10.15 (DCIN_PGD)
DC_F: C4.2, D10.1 (A1), F1.2, Q1.1 (S), Q1.2 (S), Q1.3 (S), R1.2, U3.3 (DC_F), U3.6 (DC_F)
DC_HS: C6.1, L2.1, Q7.1 (DC_HS), Q7.2 (DC_HS), Q7.3 (DC_HS), U6.9 (DC_HS)
DC_IN: F1.1, J_DCIN.1, TP1.1
DC_P: C2.1, D1.1 (K), Q1.5 (D), Q1.6 (D), Q1.7 (D), Q1.8 (D), R19.1, R20.1, R22.1, TP2.1, U3.4 (DC_P), U6.2 (DC_P)
E6_BST: C30.1, U12.6 (E6_BST)
E6_DVDD: C45.1, C46.1, U10.23 (E6_DVDD), U10.45 (E6_DVDD), U10.50 (E6_DVDD)
E6_RUN: R31.1, TP12.1, U10.26 (E6_RUN)
E6_SW: C30.2, L3.1, U12.5 (E6_SW)
FAN1_G: Q9.1 (G), R44.2
FAN1_PWM: R44.1, U10.11 (FAN1_PWM)
FAN1_SW: D7.2 (A), J_FAN1.2, Q9.3 (D)
FAN1_TACH: J_FAN1.3, R46.1, U10.13 (FAN1_TACH)
FAN2_G: Q10.1 (G), R45.2
FAN2_PWM: R45.1, U10.12 (FAN2_PWM)
FAN2_SW: D8.2 (A), J_FAN2.2, Q10.3 (D)
FAN2_TACH: J_FAN2.3, R47.1, U10.14 (FAN2_TACH)
GEIGER_CT: C53.1, U16.3 (CT)
GEIGER_EN: R56.1, U10.29 (GEIGER_EN), U16.5 (EN/UVLO)
GEIGER_IN: R48.2, TP13.1, U10.9 (GEIGER_IN)
GEIGER_PULSE: J_GEIGER.3, R48.1
GND: C1.2, C7.2, C8.2, C11.2, C12.2, C13.2, C14.2, C15.2, C19.2, C20.2, C21.2, C22.2, C23.2, C24.2, C25.2, C26.2, C27.2, C31.2, C32.2, C33.2, C34.2, C35.2, C36.2, C37.2, C38.2, C39.2, C40.2, C41.2, C42.2, C43.2, C44.2, C45.2, C46.2, C47.2, C48.2, C49.2, C50.2, C51.2, C52.2, C53.2, C54.2, C55.2, C56.2, C57.2, C58.2, D2.2 (A), D3.2 (A), D4.2 (A), D9.2 (GND), JP1.2 (B), J_BATT.1, J_BLK.5, J_BLK.6, J_BLK.7, J_BLK.11, J_DCF.2, J_GEIGER.2, J_LTG.2, J_POD.2, J_SMB.3, J_SOLAR.2, J_TAMP.2, L2.4, LED1.1 (K), LED2.1 (K), P_CN.1, Q4.1 (S), Q4.2 (S), Q4.3 (S), Q5.1 (S), Q5.2 (S), Q5.3 (S), Q9.2 (S), Q10.2 (S), R9.2, R11.2, R12.2, R15.2, R16.2, R17.2, R26.2, R39.2, R41.2, R43.2, R56.2, TP4.1, U4.2 (GND), U5.11, U5.13, U5.37, U5.39, U10.19 (GND), U10.57 (GND), U11.4 (GND), U11.9 (GND), U12.4 (GND), U13.2 (GND), U14.1 (GND), U14.5 (GND), U14.7 (GND), U15.1 (GND), U15.2 (GND), U15.3 (GND), U15.6 (GND), U15.7 (GND), U16.4 (GND), U16.7 (GND), U17.2 (GND), U17.4 (GND), U17.7 (GND), Y1.2 (G), Y1.4 (G)
GND_V: C2.2, C5.2, C6.2, D1.2 (A), D10.2 (A2), J_DCIN.2, L2.2, Q8.2 (S), R21.2, R23.2, R24.2, U3.2 (GND_V), U6.5 (GND_V)
HS_GATE: Q7.4 (HS_GATE), U6.10 (HS_GATE)
HS_OVLO: R22.2, R23.1, U6.4 (HS_OVLO)
HS_PWR: R24.1, U6.7 (HS_PWR)
HS_S: Q7.5 (HS_S), R19.2, U6.1 (HS_S)
HS_TIMER: C5.1, U6.6 (HS_TIMER)
HS_UVLO: Q8.3 (D), R20.2, R21.1, U6.3 (HS_UVLO)
IMU_CSB: R51.2, U15.12 (IMU_CSB)
IMU_INT1: U10.16 (IMU_INT1), U15.4 (IMU_INT1)
LED_A: LED1.2 (A), R27.2
LED_STAT: R33.1, U10.37 (LED_STAT)
LED_STAT_A: LED2.2 (A), R33.2
LTG_IRQ: J_LTG.5, R50.1, U10.17 (LTG_IRQ)
PRES_IO: R54.2, R55.1, U10.28 (PRES_IO)
PRES_LEAD: J_SMB.4, R54.1
PV_IN: F2.1, J_SOLAR.1
PV_P: C11.1, C12.1, C13.1, C14.1, C15.1, D4.1 (K), F2.2, Q3.5 (D), Q3.6 (D), Q3.7 (D), Q3.8 (D), R8.1, R14.1, TP5.1, U5.32, U5.33, U5.34
Q1_G: Q1.4 (G), R1.1, U3.5 (Q1_G)
Q2_G: Q2.4 (G), R18.1, U4.5 (Q2_G)
QSPI_D0: U10.53 (QSPI_D0), U11.5 (QSPI_D0)
QSPI_D1: U10.55 (QSPI_D1), U11.2 (QSPI_D1)
QSPI_D2: U10.54 (QSPI_D2), U11.3 (QSPI_D2)
QSPI_D3: U10.51 (QSPI_D3), U11.7 (QSPI_D3)
QSPI_SCLK: U10.52 (QSPI_SCLK), U11.6 (QSPI_SCLK)
QSPI_SS: R32.1, U10.56 (QSPI_SS), U11.1 (QSPI_SS)
SCL1: D9.3 (I/O2), D9.4 (I/O2), J_LTG.4, J_POD.4, R37.1, U10.7 (SCL1), U14.4 (SCL1), U15.13 (SCL1), U17.6 (SCL1)
SDA1: D9.1 (I/O1), D9.6 (I/O1), J_LTG.3, J_POD.3, R36.1, U10.6 (SDA1), U14.3 (SDA1), U15.14 (SDA1), U17.3 (SDA1)
SGP_VDD: C57.1, R57.2, U17.1 (SGP_VDD)
SHORE_INHIBIT: J_BLK.8, Q8.1 (G), R26.1, U10.18 (SHORE_INHIBIT)
SMBC: J_SMB.1, R35.1, U10.5 (SMBC)
SMBD: J_SMB.2, R34.1, U10.4 (SMBD)
SWCLK: TP10.1, U10.24 (SWCLK)
SWDIO: TP11.1, U10.25 (SWDIO)
TAMPER_IO: C52.1, R53.2, U10.27 (TAMPER_IO)
TAMPER_LEAD: J_TAMP.1, R52.1, R53.1
TRK_BG1: Q4.4 (G), U5.14
TRK_BG2: Q5.4 (G), U5.16
TRK_BOOST1: C17.1, D5.1 (K), U5.23
TRK_BOOST2: C18.1, D6.1 (K), U5.17
TRK_CSN: C16.2, R7.2, U5.2
TRK_CSP: C16.1, R6.2, U5.3
TRK_FBIN: R8.2, R9.1, U5.5
TRK_FBOUT: R10.2, R11.1, U5.6
TRK_IMONI: R16.1, U5.38
TRK_IMONO: R17.1, U5.7
TRK_INTVCC: C19.1, D5.2 (A), D6.2 (A), U5.15, U5.35, U5.36
TRK_LDO33: C20.1, U5.4
TRK_LSENSE: L1.2, R5.1, R6.1
TRK_OUT: C24.1, C25.1, C26.1, C27.1, C28.2, Q2.1 (S), Q2.2 (S), Q2.3 (S), Q6.5 (D), Q6.6 (D), Q6.7 (D), Q6.8 (D), R10.1, R18.2, TP6.1, U4.3 (TRK_OUT), U4.6 (TRK_OUT), U5.29, U5.30, U5.31
TRK_RT: R12.1, U5.12
TRK_SHDN: R14.2, R15.1, U5.1
TRK_SS: C23.1, U5.9
TRK_SW1: C17.2, L1.1, Q3.1 (S), Q3.2 (S), Q3.3 (S), Q4.5 (D), Q4.6 (D), Q4.7 (D), Q4.8 (D), U5.21
TRK_SW2: C18.2, Q5.5 (D), Q5.6 (D), Q5.7 (D), Q5.8 (D), Q6.1 (S), Q6.2 (S), Q6.3 (S), R5.2, R7.1, U5.19
TRK_TG1: Q3.4 (G), U5.22
TRK_TG2: Q6.4 (G), U5.18
TRK_VC: C22.1, R13.1, U5.8
TRK_VCC1: C21.1, R13.2
U3_VCAP: C4.1, U3.1 (U3_VCAP)
U4_VCAP: C28.1, U4.1 (U4_VCAP)
USB_DM_R: R30.1, U10.46 (USB_DM_R)
USB_DP_R: R29.1, U10.47 (USB_DP_R)
USB_E6_N: J_BLK.10, R30.2
USB_E6_P: J_BLK.9, R29.2
VIN_MON: R40.2, R41.1, U10.39 (VIN_MON)
VIN_RAW: C7.1, C8.1, D2.1 (K), J_BLK.1, J_BLK.2, J_BLK.3, J_BLK.4, L2.3, Q2.5 (D), Q2.6 (D), Q2.7 (D), Q2.8 (D), R27.1, R40.1, TP3.1, U4.4 (VIN_RAW)
WATER_A: PAD_W1.1, R38.2
WATER_SENSE: C51.1, PAD_W2.1, R39.1, U10.38 (WATER_SENSE)
XIN: C36.1, U10.20 (XIN), Y1.1
XOUT: C37.1, R28.2, Y1.3
XOUT_R: R28.1, U10.21 (XOUT_R)

Notes on the sheet:
PCB-E1 DOCK E42P
PACK ENTRY | VEHICLE AND SHORE ENTRY 9-36 V | PANEL TRACKER
PACK ENTRY: PACK CABLE ON XT60, 25 A BLADE, PADS TO THE BLOCK, PACK SMBUS LEAD (JST-XH 1x4)
VEHICLE AND SHORE ENTRY 9-36 V: F1, LM74700 IDEAL DIODE, LM5069 HOT-SWAP, SRF1260 FILTER, CLAMPS
PANEL TRACKER: J_SOLAR, F2, LT8705A BUCK-BOOST (FBIN 17.6 V, FBOUT 15.1 V, 202 kHz), ORed INTO THE RAW BUS
page 1 of 4 MeshSat field kit V2, CERN-OHL-S-2.0 PROTOTYPE, nothing built 2026-09-26
Amass XT60-M
25 A
SMBus lead to board P
SMCJ18A
solder pad
JST-VH socket
10 A mini blade
LM74700-Q1 ideal-diode controller
SMCJ40CA
SMCJ40A
BSC039N06NS 60 V 3.9 mOhm N-FET
LM5069MM-2 hot-swap controller
10mOhm 1% 2512
38.3k 1%
6.65k 1%
100n
20k
1u 100V 1210
CSD19532Q5B 100 V N-FET
2N7002
Bourns SRF1260-1R5Y dual-winding c..
1u 100V
10u 100V
green
p2,3
p2,4
PANEL TRACKER | BLOCK LANDS (MIRROR OF A22 J_DOCK)
PANEL TRACKER: J_SOLAR, F2, LT8705A BUCK-BOOST (FBIN 17.6 V, FBOUT 15.1 V, 202 kHz), ORed INTO THE RAW BUS (continued)
BLOCK LANDS (MIRROR OF A22 J_DOCK)
page 2 of 4 MeshSat field kit V2, CERN-OHL-S-2.0 PROTOTYPE, nothing built 2026-09-26
LT8705A buck-boost controller
15.0k 1%
102k 1%
7.50k 1%
5 mOhm 1% 3 W 2512 RSENSE
10uH Coilcraft XAL1510-103MED
39u 35V
115k 1%
10.0k 1%
215k 1%
SMCJ28A
100u 35V
BSC028N06NS 60 V 2.8 mOhm N-FET
BSC039N06NS 60 V N-FET
BSC028N06NS 60 V N-FET
solder lands for the 12 signal wir..
p1,4
SENSOR CONTROLLER
SENSOR CONTROLLER: 5 V BUCK, 3.3 V LDO, RP2040, QSPI FLASH, CRYSTAL, USB, BOOTSEL, PULL-UPS
page 3 of 4 MeshSat field kit V2, CERN-OHL-S-2.0 PROTOTYPE, nothing built 2026-09-26
AP63205WU-7 5 V 2 A buck for the c..
4.7uH
10u 25V
22u 10V
RP2040 sensor controller
status
BOOTSEL
decoupling of U10
W25Q16JVUXIQ 16 Mbit QSPI flash
12 MHz ABM8-272-T3
p1,2
SENSORS, WATER ELECTRODES, MONITORS, FANS, HEADERS, LID SWITCH, GEIGER SUPPLY | TEST POINTS, FLAGS
SENSORS, WATER ELECTRODES, MONITORS, FANS, HEADERS, LID SWITCH, GEIGER SUPPLY
TEST POINTS, FLAGS
page 4 of 4 MeshSat field kit V2, CERN-OHL-S-2.0 PROTOTYPE, nothing built 2026-09-26
BME688 inside climate
BMI270 six-axis IMU
SGP41-D-R4 VOC and NOx gas sensor
JST-XH 1x2
mixer fan 1 under the plate
2N7002 fan 1 low-side switch
mixer fan 2 under the plate
2N7002 fan 2 low-side switch
Geiger counter module
22R
DCF77 receiver module
AS3935 lightning sensor module
outside sensor pod on the connecto..
10k 1%
22k 1%
water electrode A
water electrode B
