meshsat/meshsat-fieldkit/v2/release/review-packets/P-P4-1f614233/native/pcb-p-pack.kicad_sch

## KiCad design v2/release/review-packets/P-P4-1f614233/native/pcb-p-pack.kicad_sch (2026-09-26)

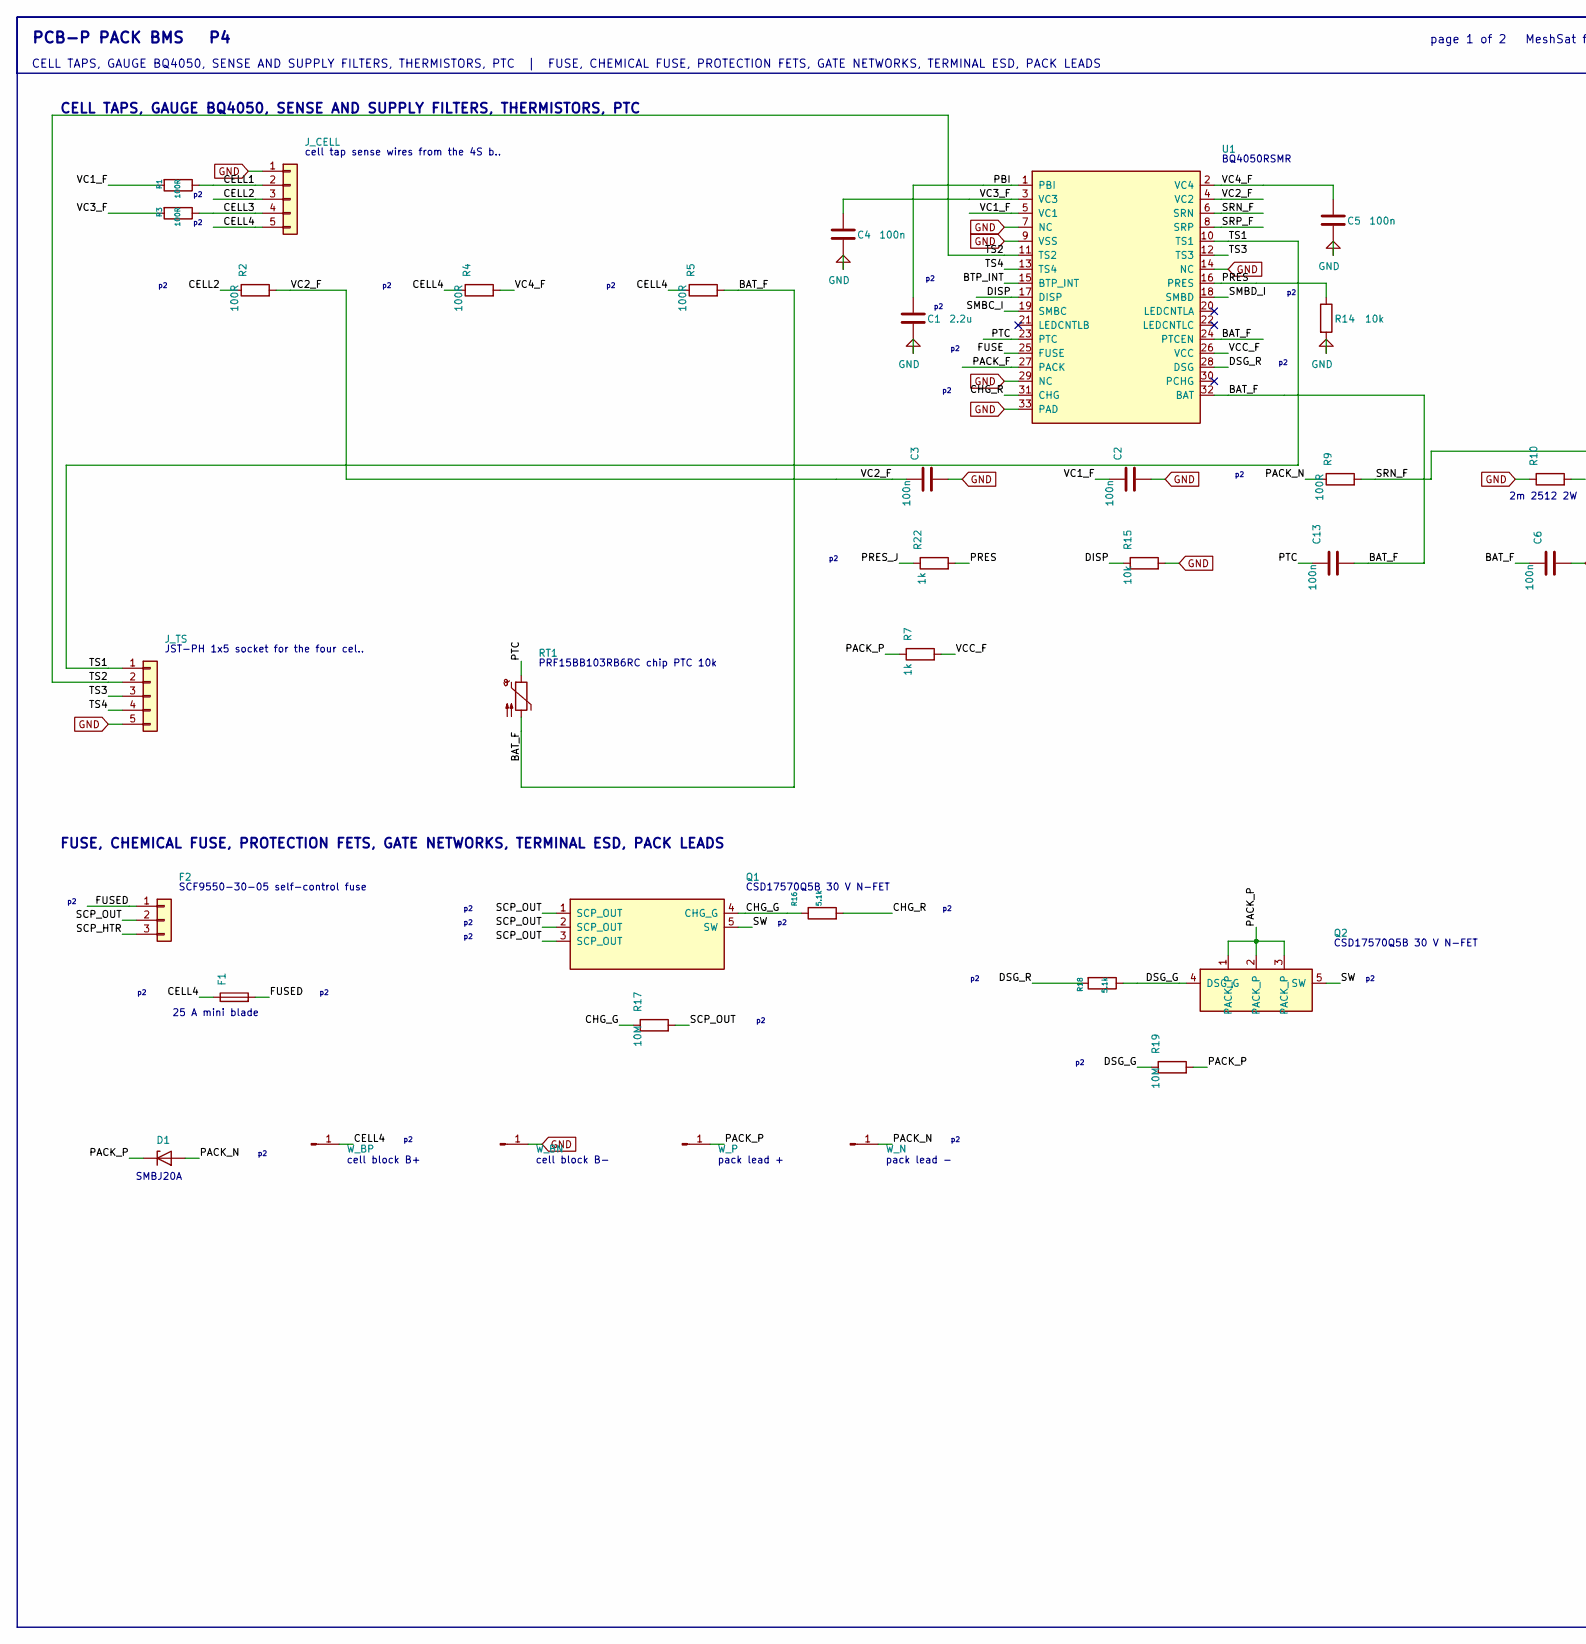
[picture p329: schematic pcb-p-pack.kicad_sch, part in row 1, column 1]

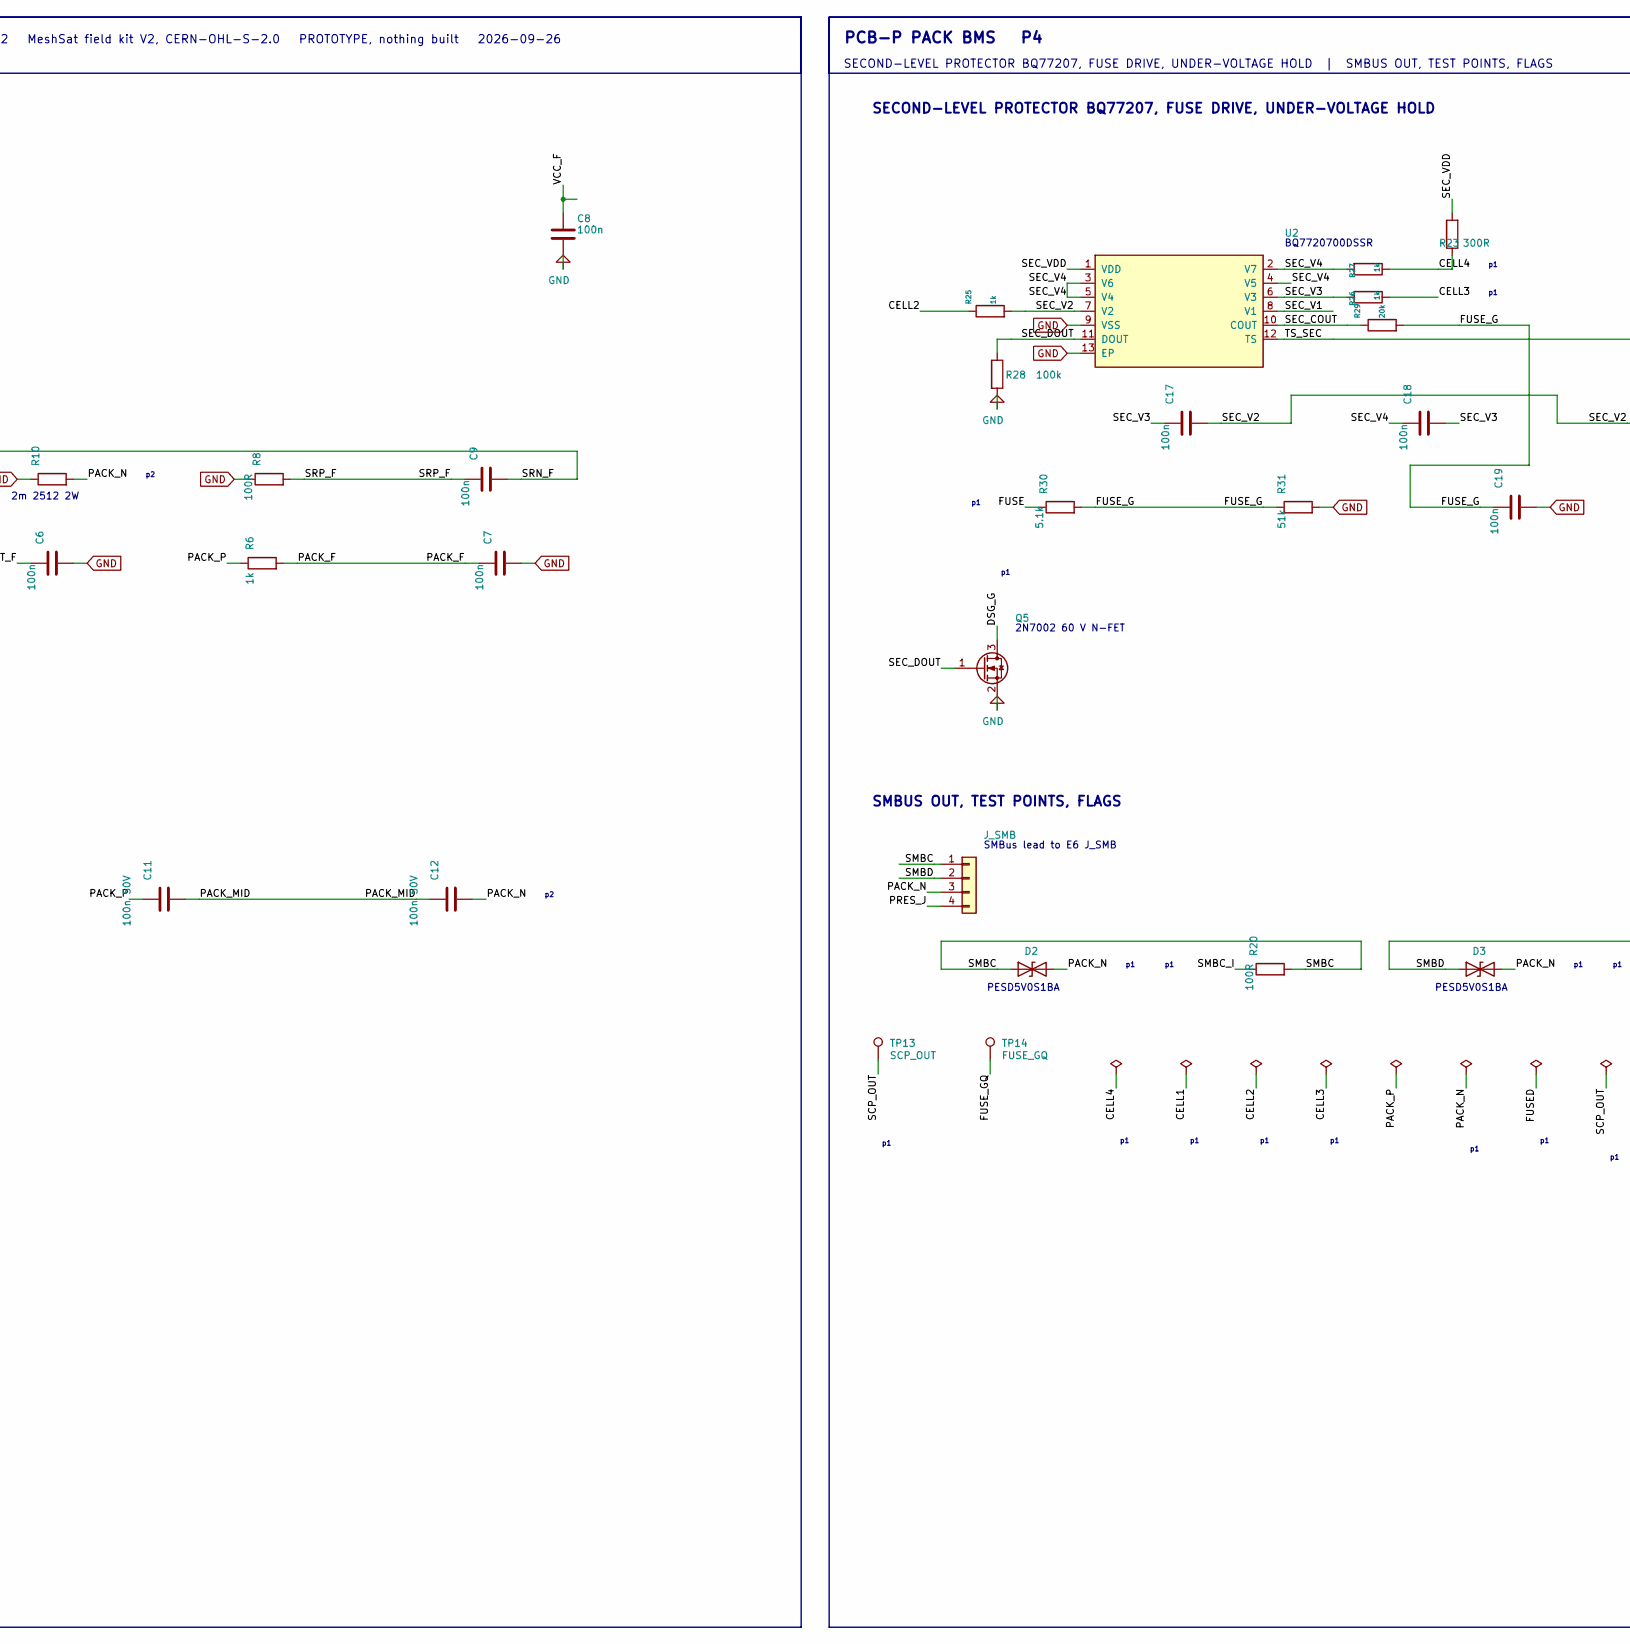
[picture p330: schematic pcb-p-pack.kicad_sch, part in row 1, column 2]

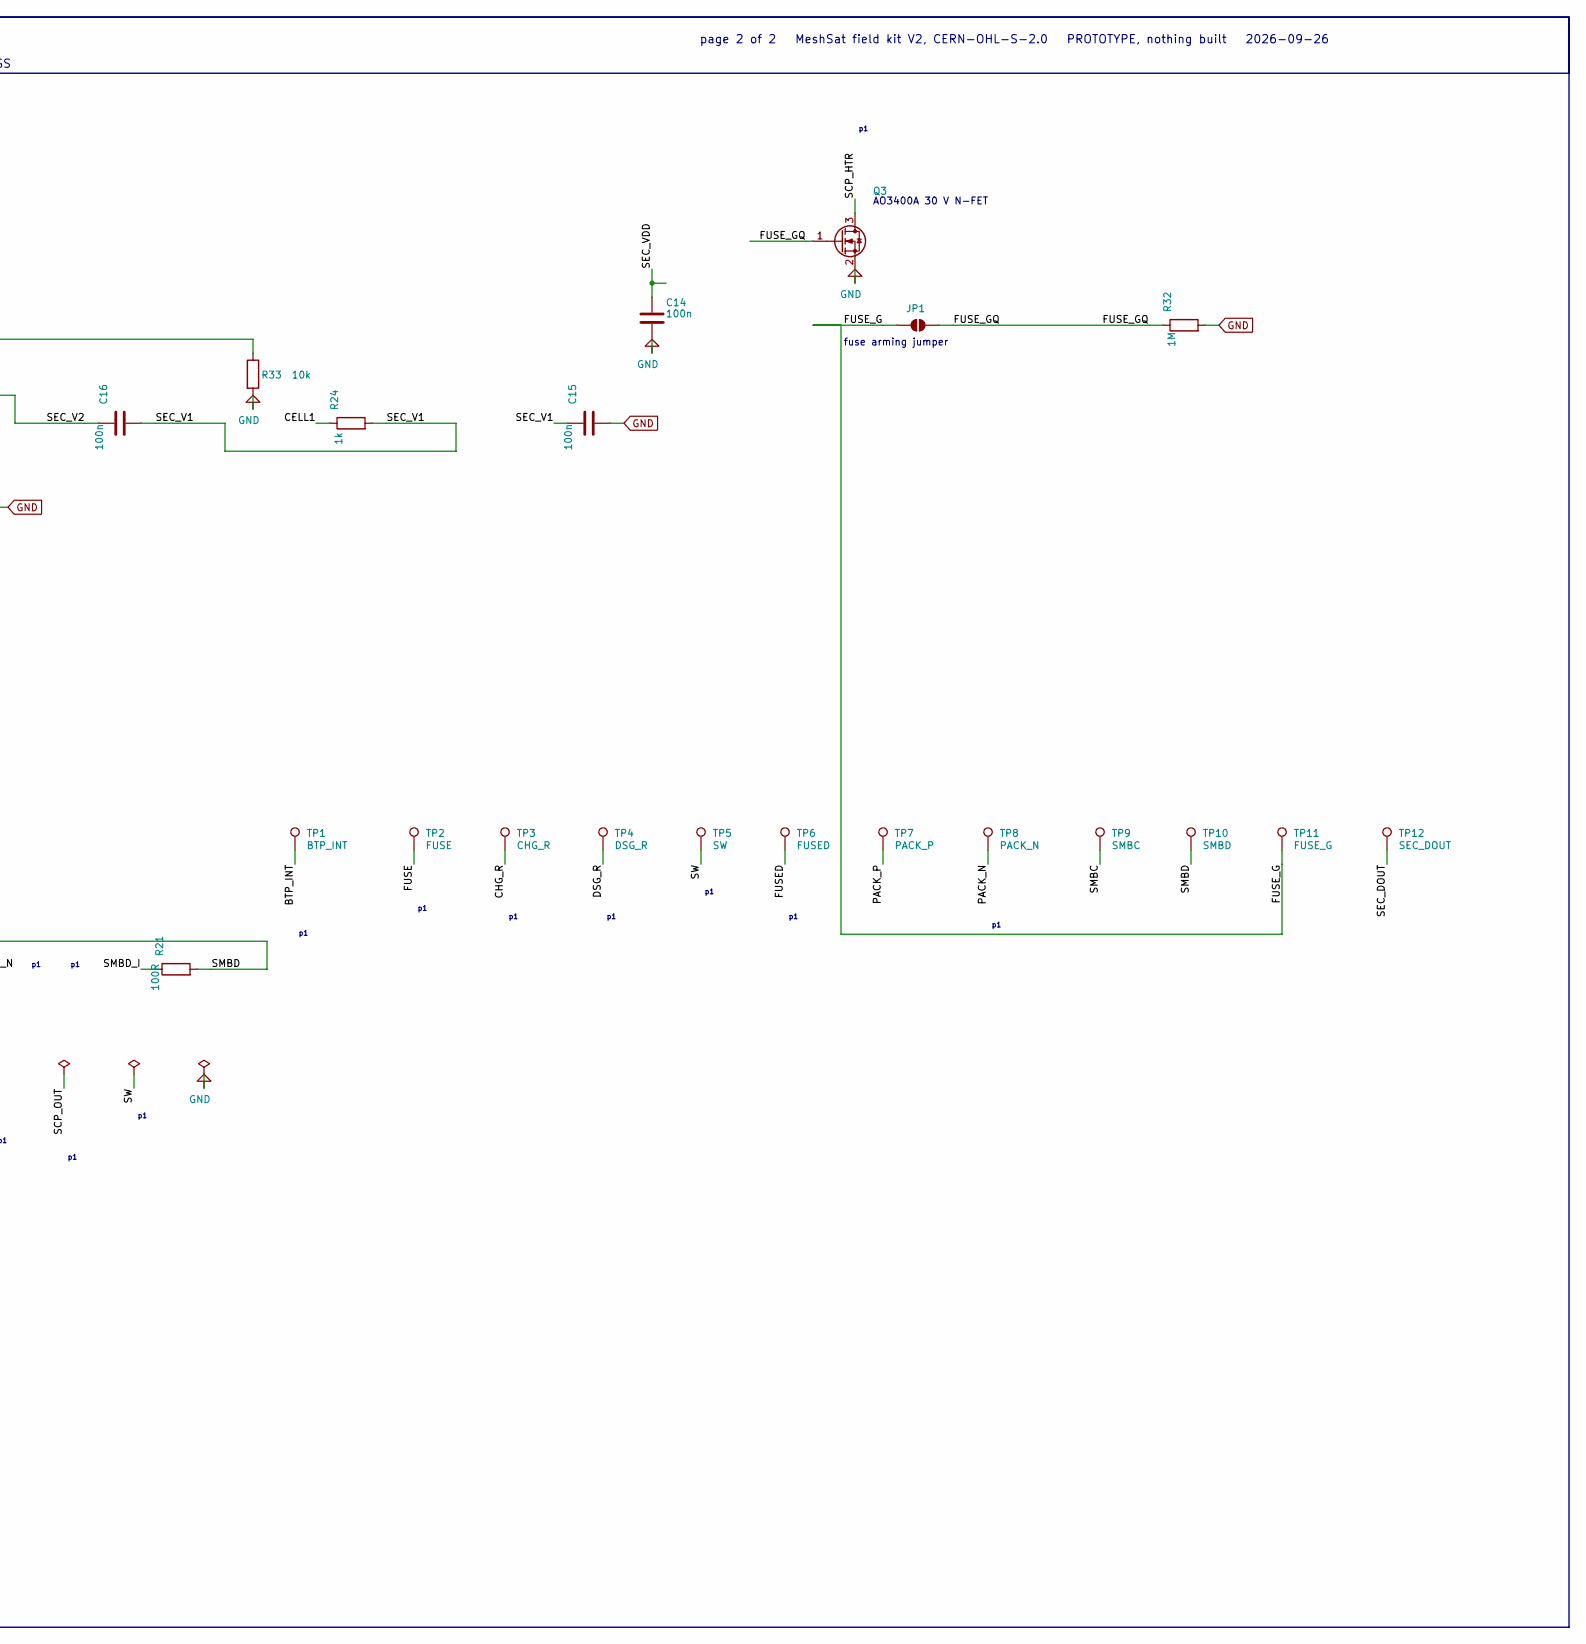
[picture p331: schematic pcb-p-pack.kicad_sch, part in row 1, column 3]

Parts:
C1: 2.2u; C_0805_2012Metric
C2, C3, C4, C5, C6, C7, C8, C9, C13, C14, C15, C16, C17, C18, C19: 100n; C_0603_1608Metric
C11: 100n 50V; C_0603_1608Metric
C12: 100n 50V; C_1206_3216Metric
D1: SMBJ20A (pack terminal clamp, unidirectional: cat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; D_SMB; LCSC C364296
D2: PESD5V0S1BA (SMBC ESD clamp to the pack side of t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; D_SOD-323; LCSC C19224
D3: PESD5V0S1BA (SMBD ESD clamp to the pack side of t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; D_SOD-323; LCSC C19224
F1: 25 A mini blade (Keystone 3568 holder): the pack'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; Fuseholder_Blade_Mini_Keystone_3568
F2: SCF9550-30-05 self-control fuse (Eaton, 30 A, 4-5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; Eaton_SCF9550_9.5x5.0mm; LCSC C3670061
JP1: fuse arming jumper: open as built, closed at comm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; SolderJumper-2_P1.3mm_Open_RoundedPad1.0x1.5mm
J_CELL: cell tap sense wires from the 4S block (JST-XH 1x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; JST_XH_B5B-XH-A_1x05_P2.50mm_Vertical
J_SMB: SMBus lead to E6 J_SMB (JST-XH 1x4): SMBC SMBD GN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; JST_XH_B4B-XH-A_1x04_P2.50mm_Vertical
J_TS: JST-PH 1x5 socket for the four cell thermistors (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; JST_PH_B5B-PH-K_1x05_P2.00mm_Vertical; LCSC C157993
Q1: CSD17570Q5B 30 V N-FET, charge switch; PowerPAK_SO-8_Single; LCSC C529279
Q2: CSD17570Q5B 30 V N-FET, discharge switch; PowerPAK_SO-8_Single; LCSC C529279
Q3: AO3400A 30 V N-FET, chemical fuse heater switch; SOT-23; LCSC C20917
Q5: 2N7002 60 V N-FET: the second level's under-volta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; SOT-23; LCSC C8545
R1, R2, R3, R4, R5, R8, R9, R20, R21: 100R; R_0603_1608Metric
R6, R7, R22, R24, R25, R26, R27: 1k; R_0603_1608Metric
R10: 2m 2512 2W (sense); R_2512_6332Metric
R14, R15, R33: 10k; R_0603_1608Metric
R16, R18, R30: 5.1k; R_0603_1608Metric
R17, R19: 10M; R_0603_1608Metric
R23: 300R; R_0603_1608Metric; LCSC C23025
R28: 100k; R_0603_1608Metric
R29: 20k; R_0603_1608Metric; LCSC C4184
R31: 51k; R_0603_1608Metric; LCSC C23196
R32: 1M; R_0603_1608Metric
RT1: PRF15BB103RB6RC chip PTC 10k, 4.7M at 130 C (Mura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; R_0402_1005Metric; LCSC C443668
TP1: BTP_INT; TestPoint_Pad_D1.5mm
TP2: FUSE; TestPoint_Pad_D1.5mm
TP3: CHG_R; TestPoint_Pad_D1.5mm
TP4: DSG_R; TestPoint_Pad_D1.5mm
TP5: SW; TestPoint_Pad_D1.5mm
TP6: FUSED; TestPoint_Pad_D1.5mm
TP7: PACK_P; TestPoint_Pad_D1.5mm
TP8: PACK_N; TestPoint_Pad_D1.5mm
TP9: SMBC; TestPoint_Pad_D1.5mm
TP10: SMBD; TestPoint_Pad_D1.5mm
TP11: FUSE_G; TestPoint_Pad_D1.5mm
TP12: SEC_DOUT; TestPoint_Pad_D1.5mm
TP13: SCP_OUT; TestPoint_Pad_D1.5mm
TP14: FUSE_GQ; TestPoint_Pad_D1.5mm
U1: BQ4050RSMR: SMBus 1.1 gas gauge, primary protecti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; Texas_RSM0032A_VQFN-32-1EP_4x4mm_P0.4mm_EP1.4x1.4mm; LCSC C157570
U2: BQ7720700DSSR: second-level cell OV 4.325 V / UV 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; WSON-12-1EP_3x2mm_P0.5mm_EP1x2.65; LCSC C3681715
W_BN: cell block B- (12 AWG from the block's negative s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; SolderWire-2.5sqmm_1x01_D2.4mm_OD3.6mm
W_BP: cell block B+ (12 AWG from the block's positive s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; SolderWire-2.5sqmm_1x01_D2.4mm_OD3.6mm
W_N: pack lead - (12 AWG to the XT60 on E6 J_BATT pin 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; SolderWire-2.5sqmm_1x01_D2.4mm_OD3.6mm
W_P: pack lead + (12 AWG to the XT60 on E6 J_BATT pin 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; SolderWire-2.5sqmm_1x01_D2.4mm_OD3.6mm

Connections:
BAT_F: C6.1, C13.2, R5.2, RT1.2, U1.24 (PTCEN), U1.32 (BAT)
BTP_INT: TP1.1, U1.15 (BTP_INT)
CELL1: J_CELL.2, R1.1, R24.1
CELL2: J_CELL.3, R2.1, R25.1
CELL3: J_CELL.4, R3.1, R26.1
CELL4: F1.1, J_CELL.5, R4.1, R5.1, R23.1, R27.1, W_BP.1
CHG_G: Q1.4 (CHG_G), R16.1, R17.1
CHG_R: R16.2, TP3.1, U1.31 (CHG)
DISP: R15.1, U1.17 (DISP)
DSG_G: Q2.4 (DSG_G), Q5.3 (D), R18.1, R19.1
DSG_R: R18.2, TP4.1, U1.28 (DSG)
FUSE: R30.1, TP2.1, U1.25 (FUSE)
FUSED: F1.2, F2.1, TP6.1
FUSE_G: C19.1, JP1.1 (A), R29.2, R30.2, R31.1, TP11.1
FUSE_GQ: JP1.2 (B), Q3.1 (G), R32.1, TP14.1
GND: C1.2, C2.2, C3.2, C4.2, C5.2, C6.2, C7.2, C8.2, C14.2, C15.2, C19.2, J_CELL.1, J_TS.5, Q3.2 (S), Q5.2 (S), R8.1, R10.1, R14.2, R15.2, R28.2, R31.2, R32.2, R33.2, U1.7 (NC), U1.9 (VSS), U1.14 (NC), U1.29 (NC), U1.33 (PAD), U2.9 (VSS), U2.13 (EP), W_BN.1
PACK_F: C7.1, R6.2, U1.27 (PACK)
PACK_MID: C11.2, C12.1
PACK_N: C12.2, D1.2 (A), D2.2 (A2), D3.2 (A2), J_SMB.3, R9.1, R10.2, TP8.1, W_N.1
PACK_P: C11.1, D1.1 (K), Q2.1 (PACK_P), Q2.2 (PACK_P), Q2.3 (PACK_P), R6.1, R7.1, R19.2, TP7.1, W_P.1
PBI: C1.1, U1.1 (PBI)
PRES: R14.1, R22.2, U1.16 (PRES)
PRES_J: J_SMB.4, R22.1
PTC: C13.1, RT1.1, U1.23 (PTC)
SCP_HTR: F2.3, Q3.3 (D)
SCP_OUT: F2.2, Q1.1 (SCP_OUT), Q1.2 (SCP_OUT), Q1.3 (SCP_OUT), R17.2, TP13.1
SEC_COUT: R29.1, U2.10 (COUT)
SEC_DOUT: Q5.1 (G), R28.1, TP12.1, U2.11 (DOUT)
SEC_V1: C15.1, C16.2, R24.2, U2.8 (V1)
SEC_V2: C16.1, C17.2, R25.2, U2.7 (V2)
SEC_V3: C17.1, C18.2, R26.2, U2.6 (V3)
SEC_V4: C18.1, R27.2, U2.2 (V7), U2.3 (V6), U2.4 (V5), U2.5 (V4)
SEC_VDD: C14.1, R23.2, U2.1 (VDD)
SMBC: D2.1 (A1), J_SMB.1, R20.2, TP9.1
SMBC_I: R20.1, U1.19 (SMBC)
SMBD: D3.1 (A1), J_SMB.2, R21.2, TP10.1
SMBD_I: R21.1, U1.18 (SMBD)
SRN_F: C9.2, R9.2, U1.6 (SRN)
SRP_F: C9.1, R8.2, U1.8 (SRP)
SW: Q1.5 (SW), Q2.5 (SW), TP5.1
TS1: J_TS.1, U1.10 (TS1)
TS2: J_TS.2, U1.11 (TS2)
TS3: J_TS.3, U1.12 (TS3)
TS4: J_TS.4, U1.13 (TS4)
TS_SEC: R33.1, U2.12 (TS)
VC1_F: C2.1, R1.2, U1.5 (VC1)
VC2_F: C3.1, R2.2, U1.4 (VC2)
VC3_F: C4.1, R3.2, U1.3 (VC3)
VC4_F: C5.1, R4.2, U1.2 (VC4)
VCC_F: C8.1, R7.2, U1.26 (VCC)

Notes on the sheet:
PCB-P PACK BMS P4
CELL TAPS, GAUGE BQ4050, SENSE AND SUPPLY FILTERS, THERMISTORS, PTC | FUSE, CHEMICAL FUSE, PROTECTION FETS, GATE NETWORKS, TERMINAL ESD, PACK LEADS
CELL TAPS, GAUGE BQ4050, SENSE AND SUPPLY FILTERS, THERMISTORS, PTC
FUSE, CHEMICAL FUSE, PROTECTION FETS, GATE NETWORKS, TERMINAL ESD, PACK LEADS
page 1 of 2 MeshSat field kit V2, CERN-OHL-S-2.0 PROTOTYPE, nothing built 2026-09-26
cell tap sense wires from the 4S b..
BQ4050RSMR
2m 2512 2W
JST-PH 1x5 socket for the four cel..
PRF15BB103RB6RC chip PTC 10k
SCF9550-30-05 self-control fuse
25 A mini blade
CSD17570Q5B 30 V N-FET
SMBJ20A
cell block B+
cell block B-
pack lead +
pack lead -
SECOND-LEVEL PROTECTOR BQ77207, FUSE DRIVE, UNDER-VOLTAGE HOLD | SMBUS OUT, TEST POINTS, FLAGS
SECOND-LEVEL PROTECTOR BQ77207, FUSE DRIVE, UNDER-VOLTAGE HOLD
SMBUS OUT, TEST POINTS, FLAGS
page 2 of 2 MeshSat field kit V2, CERN-OHL-S-2.0 PROTOTYPE, nothing built 2026-09-26
BQ7720700DSSR
AO3400A 30 V N-FET
fuse arming jumper
2N7002 60 V N-FET
SMBus lead to E6 J_SMB
PESD5V0S1BA
