meshsat/meshsat-fieldkit/v2/release/handover/H1/v2/ecad/pcb-a-power-a23/pcb-a-power.kicad_sch

## KiCad design v2/release/handover/H1/v2/ecad/pcb-a-power-a23/pcb-a-power.kicad_sch (2026-09-26)

Schematic: pcb-a-power.kicad_sch

Parts:
C1, C2: 47u 25V; C_1206_3216Metric
C3, C29, C30, C41, C42, C54, C120, C159: 10u 25V 1210; C_1210_3225Metric
C4, C19: 1u; C_0603_1608Metric
C5, C86: 220n; C_0603_1608Metric; LCSC C160828
C6, C147: 680p; C_0603_1608Metric; LCSC C30816
C7: 4.7u; C_0805_2012Metric; LCSC C354262
C8, C60, C71, C78, C89, C136, C143: 4.7u; C_0805_2012Metric
C9, C10, C16, C17, C34, C46, C61, C62, C72, C73, C79, C80, C90, C91, C137, C144: 100n 25V; C_0603_1608Metric
C11, C12, C83, C84, C85, C176, C177: 10u 100V X7R 1210; C_1210_3225Metric
C13, C14, C15, C20, C21, C22, C35, C36, C47, C48, C63, C64, C65, C66, C67, C74, C81, C82, C92, C108, C109, C110, C111, C116, C117, C118, C119, C181, C182, C183, C184, C185, C186, C187, C188, C189, C201, C202, C203, C204, C205, C206: 10u 50V X7R 1210; C_1210_3225Metric
C18: 3.3u; C_0805_2012Metric
C23, C24, C25, C156, C161, C162: 22u 25V 1210; C_1210_3225Metric
C26, C53, C98, C100, C102, C121, C154, C158: 10n; C_0603_1608Metric
C27, C123, C124, C125, C126, C127, C128, C129, C130, C131, C132, C138, C139, C145, C146: 1n; C_0603_1608Metric
C28, C40, C52, C93, C95, C99, C101, C103, C104, C106, C107, C122, C153, C155, C157, C160, C192, C193, C194, C195, C196, C197, C198: 100n; C_0603_1608Metric
C31, C32, C33, C43, C44, C45, C55, C56: 22u 10V X7R 1210; C_1210_3225Metric
C37, C38, C39, C49, C50, C51: 22u 25V 1210; C_1210_3225Metric; LCSC C2918511
C57, C68, C75, C113, C115, C212, C214, C215, C216, C217, C218, C219, C220, C221, C222, C223: 100n; C_0603_1608Metric; LCSC C14663
C58, C87: 1.5n; C_0603_1608Metric; LCSC C37788
C59, C70, C77, C88, C135, C142: 47n; C_0603_1608Metric
C69, C134, C141, C191: 1n; C_0603_1608Metric; LCSC C1588
C76, C133, C140, C148, C149, C151: 470p; C_0603_1608Metric; LCSC C27694
C94: 220n; C_0603_1608Metric
C96, C97: 330p; C_0603_1608Metric
C112, C114: 3.3n; C_0603_1608Metric
C150: 560p; C_0603_1608Metric; LCSC C43962
C152: 680n; C_0603_1608Metric; LCSC C107067
C163, C178, C179, C180, C199, C200: 330u 35V Panasonic EEHZK1V331P hybrid polymer (10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; CP_Elec_10x10; LCSC C278516
C164, C165, C166, C167, C168, C169, C172, C173: 150u 25V Panasonic EEHZK1E151XP hybrid polymer (7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; CP_Elec_6.3x7.7; LCSC C542453
C170, C171, C174, C175: 470u 25V Panasonic EEHZK1E471P hybrid polymer (10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; CP_Elec_10x10; LCSC C242138
C190, C211: 10n; C_0603_1608Metric; LCSC C57112
C207, C210: 1u 100V 1210; C_1210_3225Metric; LCSC C382212
C208, C209: 1u; C_0603_1608Metric; LCSC C15849
C213: 2.2n; C_0603_1608Metric; LCSC C16033
D1: SMCJ18A (VBAT clamp); D_SMC; LCSC C374030
D2: SMCJ40A (VIN_RAW clamp behind E6's filter: 40 V s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; D_SMC; LCSC C224052
D3: SMBJ5.0A; D_SMB
D4: SMBJ18A (VBUS clamp at the outlet); D_SMB
D5, D6, D7, D8, D9, D10, D11, D12, D13, D14, D15, D16, D17, D18: BAT46W-7-F Schottky 100V (bootstrap); D_SOD-123; LCSC C83152
D19, D20, D21: BAT46W-7-F Schottky 100V (VIN blocking); D_SOD-123; LCSC C83152
D22: BZT52C12-7-F zener, the restart guard's pull-up c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; D_SOD-123; LCSC C124196
F1: 25 A mini blade (Keystone 3568 holder): pack node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; Fuseholder_Blade_Mini_Keystone_3568
J_5V_DEV: USB device rail to B16 (JST-VH): + -; JST_VH_B2P-VH_1x02_P3.96mm_Vertical; LCSC C274411
J_5V_S1: slot 1 5.1 V rail to B16 (JST-VH, 16 AWG): + -; JST_VH_B2P-VH_1x02_P3.96mm_Vertical; LCSC C274411
J_5V_S2: slot 2 5.1 V rail to B16 (JST-VH, 16 AWG): + -; JST_VH_B2P-VH_1x02_P3.96mm_Vertical; LCSC C274411
J_5V_S3: slot 3 5.1 V rail to B16 (JST-VH, 16 AWG): + -; JST_VH_B2P-VH_1x02_P3.96mm_Vertical; LCSC C274411
J_54V: 54 V to the PoE injector on B16 (JST-VH): + -; JST_VH_B2P-VH_1x02_P3.96mm_Vertical; LCSC C274411
J_AB1: A-B interconnect (IDC 2x13, top side) to B16's un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; IDC-Header_2x13_P2.54mm_Vertical_NarrowPad
J_AB2: A-B wall-port ribbon (IDC 2x5): the wall USB pair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; IDC-Header_2x05_P2.54mm_Vertical_NarrowPad
J_BM1, J_BM2, J_BM3, J_BM4, J_BM5, J_BM6, J_BM7, J_BM8, J_BM9, J_BM10, J_BM11: SMP-MAX slide-on receptacle R222M00720 (underside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; Radiall_SMPMAX_R222M00720
J_CN1, J_CN2, J_CN3, J_CN4: 9 A spring pin, pack return (Mill-Max 0858 class,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; Mill-Max_0858_power_pin
J_CP1, J_CP2, J_CP3, J_CP4: 9 A spring pin, CELL+ (Mill-Max 0858 class, dock 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; Mill-Max_0858_power_pin
J_DOCK: spring pins to the dock block (2x6, Preci-Dip 813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; PogoPins_2x6
J_HEAT: JST-XH 1x2 socket: the pack heater mat (12 V, 7.5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; JST_XH_B2B-XH-A_1x02_P2.50mm_Vertical; LCSC C158012
J_HF: 12.0 V to the QMX HF unit in its lid tray (JST-VH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; JST_VH_B2P-VH_1x02_P3.96mm_Vertical; LCSC C274411
J_MAINSW: JST-XH 1x2 socket: the MAIN button lead from the 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; JST_XH_B2B-XH-A_1x02_P2.50mm_Vertical; LCSC C158012
J_MEZZ1: D8 mezzanine harness (IDC 2x8): its USB pair, the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; IDC-Header_2x08_P2.54mm_Vertical_NarrowPad
J_MEZZ_PWR1: D8 mezzanine 5 V (JST-VH): + -; JST_VH_B2P-VH_1x02_P3.96mm_Vertical; LCSC C274411
J_MON: monitor supply lead to the Xenarc (JST-VH): + -; JST_VH_B2P-VH_1x02_P3.96mm_Vertical; LCSC C274411
J_PA: 13.8 V to the PA module on the face plate (JST-VH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; JST_VH_B2P-VH_1x02_P3.96mm_Vertical; LCSC C274411
J_PRE1: pre-charge pin, longer, mates first (32.24 AX); Mill-Max_0858_power_pin
J_RF1, J_RF2, J_RF3, J_RF4, J_RF5, J_RF6, J_RF7, J_RF8, J_RF9, J_RF10, J_RF11: SMA jack, Amphenol 132134-11 vertical (pigtail to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; SMA_Amphenol_132134-11_Vertical; LCSC C3174425
J_USBC_OUT: wall USB-C outlet, power only (pigtail header): V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; PinHeader_1x05_P2.54mm_Vertical
J_USBW: JST-PH 1x4 socket: the Glenair 233-370 USB host f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; JST_PH_B4B-PH-K_1x04_P2.00mm_Vertical; LCSC C131334
L1: 10uH XAL1010-103ME (Isat 17.5 A); L_Coilcraft_XAL1010-XXX; LCSC C6358489
L2: 3.3uH XAL6030-332ME (Isat 12.2 A); L_Coilcraft_XAL6060-XXX
L3, L5: 4.7uH XAL6060-472ME (Isat 11 A); L_Coilcraft_XAL6060-XXX
L4, L6, L8: 6.8uH XAL1010-682ME (Isat 21.8 A); L_Coilcraft_XAL1010-XXX
L7: 4.7uH XAL4030-472ME; L_Coilcraft_XAL4030-XXX
L9, L11: 6.8uH XAL1010-682ME; L_Coilcraft_XAL1010-XXX
L10: 15uH XAL1010-153ME (Isat 15.5 A); L_Coilcraft_XAL1010-XXX; LCSC C2802562
L12: 15uH XAL4040-153ME (Isat 2.9 A); L_Coilcraft_XAL4040-XXX
Q1: 2N7002: panel controller high = pull KILL low = p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; SOT-23
Q2, Q3, Q4, Q5, Q17, Q18, Q19, Q20, Q28, Q29, Q30, Q31, Q32, Q33, Q34, Q35: CSD19532Q5B 100 V N-FET (4.6 mOhm at VGS 6 V, Pow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; PowerPAK_SO-8_Single; LCSC C473333
Q6: 2N7002: CHG_INHIBIT high = ILIM_HIZ low = charger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; SOT-23
Q7, Q8, Q9, Q10, Q11, Q12, Q13, Q14, Q15, Q16, Q21, Q22, Q23, Q24, Q25, Q26: CSD18510Q5B 40 V N-FET; PowerPAK_SO-8_Single
Q27: CSD18510Q5B 40 V N-FET (VBUS switch); PowerPAK_SO-8_Single
Q36: 2N7002: FE_RUN high = latch sense held at 0 V (1 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; SOT-23; LCSC C8545
Q37: 2N7002: FE_RUN high = bleed off (1 G, 2 S, 3 D); SOT-23; LCSC C8545
Q38: CSD19532Q5B 100 V N-FET (the VBUS20 bleed switch); PowerPAK_SO-8_Single; LCSC C473333
R1: 10R 2W 2512; R_2512_6332Metric
R2, R4, R13, R30, R34, R38, R42, R57, R73, R116, R118, R123, R128, R145, R171, R178, R193: 100k; R_0603_1608Metric
R3, R22, R23, R25, R44, R91, R95, R99, R110, R117, R142, R187: 10k; R_0603_1608Metric
R5: 1k; R_0603_1608Metric
R6: 240k 1%; R_0603_1608Metric
R7, R29, R33, R37, R41, R49, R51, R61, R67, R75, R134, R192: 10k 1%; R_0603_1608Metric
R8, R46, R52, R62, R68, R78, R115: 40.2k (206 kHz); R_0603_1608Metric
R10: 15k; R_0603_1608Metric; LCSC C22809
R11, R65, R81, R138: 10mOhm 1% 2512 (ISNS); R_2512_6332Metric
R12, R56, R122, R127, R170, R177: 5mOhm 1% 2512 (CS); R_2512_6332Metric
R14: 91k 1%; R_0603_1608Metric; LCSC C23265
R15, R58, R102, R124: 10k 1%; R_0603_1608Metric; LCSC C25804
R16: 10mOhm 1% 2512 (RAC, input current sense); R_2512_6332Metric
R17: 5mOhm 1% 2512 (RSR, charge current sense); R_2512_6332Metric
R18, R146, R147, R148, R149: 10R; R_0603_1608Metric
R19: 16.5k 1%; R_0603_1608Metric
R20: 34.8k 1%; R_0603_1608Metric
R21, R103, R104, R111, R112, R113, R114, R143, R190: 4.7k; R_0603_1608Metric
R24: 10k (PSYS load); R_0603_1608Metric
R26: 13.3k 1% (CELL_BATPRESZ: 4S, 75 percent of VDDA); R_0603_1608Metric; LCSC C25952
R27: 40.2k 1%; R_0603_1608Metric
R28, R32, R36, R40: 53.6k 1%; R_0603_1608Metric
R31, R39: 5mOhm 1% 2512 (shunt); R_2512_6332Metric
R35, R43, R55: 6mOhm 1% 2512 (ISNS); R_2512_6332Metric; LCSC C843882
R45, R47: 68k (RT: 500 kHz); R_0603_1608Metric
R48: 31.6k 1%; R_0603_1608Metric
R50: 162k 1%; R_0603_1608Metric
R54: 6.8k; R_0603_1608Metric; LCSC C23212
R59, R125: 15k 1%; R_0603_1608Metric; LCSC C22809
R60, R191: 140k 1%; R_0603_1608Metric
R64, R80: 3.3k; R_0603_1608Metric; LCSC C22978
R66: 665k 1%; R_0603_1608Metric
R70: 4.7k; R_0603_1608Metric; LCSC C23162
R71: 20mOhm 1% 2512 (ISNS); R_2512_6332Metric
R72: 10mOhm 1% 2512 (CS); R_2512_6332Metric
R74, R133: 62k 1%; R_0603_1608Metric
R76: 105k 1%; R_0603_1608Metric
R77: 20k 1% (R_FBL); R_0603_1608Metric
R90: 750R 1% (ILM: 1.2 A); R_0603_1608Metric
R92, R96: 143k 1%; R_0603_1608Metric; LCSC C22877
R93, R97, R101, R189: 10k 1% (OVLO); R_0603_1608Metric
R94: 909R 1% (ILM: 1.0 A); R_0603_1608Metric
R98: 453R 1% (ILM: 2.0 A); R_0603_1608Metric
R100, R188: 40.2k 1%; R_0603_1608Metric; LCSC C12447
R119, R120, R121, R126, R135, R172, R179: 100k (MODE: CCM); R_0603_1608Metric
R129, R131: 22k; R_0603_1608Metric
R130, R132: 2.2k; R_0603_1608Metric; LCSC C4190
R136: 21.0k 1% (R_FBL2: 9 V when CTL2 is low); R_0603_1608Metric
R137: 14.0k 1% (R_FBL1: 15 V when CTL1 is low too); R_0603_1608Metric
R139: 43R 1W 2512 (DSCG); R_2512_6332Metric
R140: 1M (GD to VPWR, 9.1.3); R_0603_1608Metric
R141: 698k; R_0603_1608Metric
R150, R152, R154, R156, R158, R173, R180: 100R 1% (CS filter, Kelvin from the shunt's top); R_0603_1608Metric
R151, R153, R155, R157, R159, R174, R181: 100R 1% (CSG filter, Kelvin from the shunt's grou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; R_0603_1608Metric
R160, R162, R164, R166, R168, R175, R182: 100R 1% (ISNS+ filter, Kelvin from the shunt's ou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; R_0603_1608Metric
R161, R163, R165, R167, R169, R176, R183: 100R 1% (ISNS- filter, Kelvin from the shunt's ra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; R_0603_1608Metric
R184: 39k 1%; R_0603_1608Metric; LCSC C23153
R186: 1k 1% (ILM: 0.89 A); R_0603_1608Metric; LCSC C21190
R194: 20k 1%; R_0603_1608Metric
R195: 2k; R_0603_1608Metric; LCSC C22975
R196: 1k; R_0603_1608Metric; LCSC C21190
R197, R198, R201, R206, R207, R208: 100k; R_0603_1608Metric; LCSC C25803
R199: 47k; R_0603_1608Metric; LCSC C25819
R200: 33k; R_0603_1608Metric; LCSC C4216
R202, R203, R204, R205: 510R 1W 2512 (VBUS20 bleed); R_2512_6332Metric; LCSC C36171
TP3: EXP2_SP3; TestPoint_Pad_D1.5mm
TP4: EXP2_SP4; TestPoint_Pad_D1.5mm
TP5: EXP2_SP5; TestPoint_Pad_D1.5mm
TP6: EXP2_SP6; TestPoint_Pad_D1.5mm
TP7: EXP2_SP7; TestPoint_Pad_D1.5mm
TP8: EXP2_SP8; TestPoint_Pad_D1.5mm
TP9: VBAT; TestPoint_Pad_D1.5mm
TP10: GND; TestPoint_Pad_D1.5mm
TP11: +3V3; TestPoint_Pad_D1.5mm
TP12: VBUS20; TestPoint_Pad_D1.5mm
TP13: VIN_RAW; TestPoint_Pad_D1.5mm
TP14: CELL+; TestPoint_Pad_D1.5mm
TP15: EMCON_HW; TestPoint_Pad_D1.5mm
TP16: RAIL_EN; TestPoint_Pad_D1.5mm
TP17: SDA; TestPoint_Pad_D1.5mm
TP18: SCL; TestPoint_Pad_D1.5mm
TP19: IADPT; TestPoint_Pad_D1.5mm
TP20: IBAT; TestPoint_Pad_D1.5mm
TP21: DOCK_SPARE; TestPoint_Pad_D1.5mm
TP22: REGN; TestPoint_Pad_D1.5mm
TP23: USBX_EN; TestPoint_Pad_D1.5mm
TP24: USBX_FLT; TestPoint_Pad_D1.5mm
TP25: EXP2_SPC; TestPoint_Pad_D1.5mm
TP26: EXP2_SPD; TestPoint_Pad_D1.5mm
TP27: AB_SPARE; TestPoint_Pad_D1.5mm
U1: LTC2954ITS8-1 push-button on/off controller, -40 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; TSOT-23-8; LCSC C2657885
U2: LM5176PWPR buck-boost controller, VBUS20 from VIN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; HTSSOP-28-1EP_4.4x9.7mm_P0.65mm_EP2.85x5.4mm; LCSC C442493
U3: BQ25731RSNR 1 to 5 cell buck-boost charger, 4S fr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; QFN-32-1EP_4x4mm_P0.4mm_EP2.65x2.65mm; LCSC C2871872
U4: AP64500SP-13 5 A buck, 5.1 V rail +5V_S1; SOIC-8-1EP_3.9x4.9mm_P1.27mm_EP2.29x3mm; LCSC C2070920
U5: LM5176PWPR buck-boost controller, +5V_S2 from VBAT; HTSSOP-28-1EP_4.4x9.7mm_P0.65mm_EP2.85x5.4mm; LCSC C442493
U6: AP64500SP-13 5 A buck, 5.1 V rail +5V_S3; SOIC-8-1EP_3.9x4.9mm_P1.27mm_EP2.29x3mm; LCSC C2070920
U7: LM5176PWPR buck-boost controller, +5V_DEV from VB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; HTSSOP-28-1EP_4.4x9.7mm_P0.65mm_EP2.85x5.4mm; LCSC C442493
U8: INA226 rail monitor +5V_S1; VSSOP-10_3x3mm_P0.5mm; LCSC C49851
U9: INA226 rail monitor +5V_S2; VSSOP-10_3x3mm_P0.5mm; LCSC C49851
U10: INA226 rail monitor +5V_S3; VSSOP-10_3x3mm_P0.5mm; LCSC C49851
U11: INA226 rail monitor +5V_DEV; VSSOP-10_3x3mm_P0.5mm; LCSC C49851
U12: TPS62933DRLR 3 A buck, 3.3 V logic; SOT-583-8; LCSC C3200405
U13: LM5176PWPR buck-boost controller, +13V8_PA from V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; HTSSOP-28-1EP_4.4x9.7mm_P0.65mm_EP2.85x5.4mm; LCSC C442493
U14: INA226 PA rail monitor (0x46); VSSOP-10_3x3mm_P0.5mm; LCSC C49851
U15: LM5176PWPR buck-boost controller, +12V_HF from VB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; HTSSOP-28-1EP_4.4x9.7mm_P0.65mm_EP2.85x5.4mm; LCSC C442493
U16: LM5176PWPR buck-boost controller, +54V_POE from V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; HTSSOP-28-1EP_4.4x9.7mm_P0.65mm_EP2.85x5.4mm; LCSC C442493
U17: INA226 PoE rail monitor (0x47); VSSOP-10_3x3mm_P0.5mm; LCSC C49851
U18: TPS25740ARGER USB-C PD source controller, 45 W ou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; QFN-24-1EP_4x4mm_P0.5mm_EP2.5x2.5mm; LCSC C544309
U19: LM5176PWPR buck-boost controller, PD_VPWR from VB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; HTSSOP-28-1EP_4.4x9.7mm_P0.65mm_EP2.85x5.4mm; LCSC C442493
U21: TPS259631DDAR eFuse VBAT -> VMON (750R 1% (ILM: 1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; SOIC-8-1EP_3.9x4.9mm_P1.27mm_EP2.29x3mm; LCSC C2155778
U22: TPS259631DDAR eFuse VBAT -> VHEAT_IN (909R 1% (IL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; SOIC-8-1EP_3.9x4.9mm_P1.27mm_EP2.29x3mm; LCSC C2155778
U23: TPS259631DDAR eFuse +5V_DEV -> +5V_D8 (453R 1% (I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; SOIC-8-1EP_3.9x4.9mm_P1.27mm_EP2.29x3mm; LCSC C2155778
U26: SN74LVC08APWR quad AND: the outlet interlock for 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; TSSOP-14_4.4x5mm_P0.65mm; LCSC C465737
U27: PCA9555PW (0x21): enables and status; TSSOP-24_4.4x7.8mm_P0.65mm; LCSC C2864778
U28: PCA9555PW (0x24): power-good lines, spares; TSSOP-24_4.4x7.8mm_P0.65mm; LCSC C2864778
U29: USBLC6-2SC6; SOT-23-6; LCSC C7519
U30: SN74LVC1G00DBVR NAND: OUTLET_OK = NOT (TR_APRS AN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; SOT-23-5; LCSC C7826
U31: TPD2E2U06QDBZRQ1 low-capacitance ESD array, USB-C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; SOT-23; LCSC C488151
U32: TPS259631DDAR eFuse +5V_DEV -> VBUS_WALL (1k 1% (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; SOIC-8-1EP_3.9x4.9mm_P1.27mm_EP2.29x3mm; LCSC C2155778
U33: TPS62933DRLR 3 A buck, 12.0 V heater rail; SOT-583-8; LCSC C3200405
U34: TPS37A010122DSKR 65 V OV/UV supervisor: the FE's 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; WSON-10-1EP_2.5x2.5mm_P0.5mm_EP1.2x2mm; LCSC C3685740
U35: SN74AUP1G08DBVR AND: PA_TXOK = TX_INHIBIT_n AND E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; SOT-23-5; LCSC C139409
U36: SN74AUP1G08DBVR AND: PA_EN = PA_TXOK AND PA_SW_EN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; SOT-23-5; LCSC C139409
U37: SN74AUP1G08DBVR AND: HF_TXOK = TX_INHIBIT_n AND E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; SOT-23-5; LCSC C139409
U38: SN74AUP1G08DBVR AND: HF_EN = HF_TXOK AND HF_SW_EN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; SOT-23-5; LCSC C139409

Connections:
+3V3: C55.1, C56.1, C104.1, C106.1, C107.1, C153.1, C215.1, C216.1, C217.1, C218.1, D3.1 (K), J_MEZZ1.13, L7.2, R3.2, R4.2, R13.2, R22.2, R23.2, R42.2, R44.2, R48.1, R57.2, R73.2, R91.2, R95.2, R99.2, R110.2, R117.2, R123.2, R128.2, R142.2, R171.2, R178.2, R187.2, TP11.1, U8.6 (+3V3), U9.2 (+3V3), U9.6 (+3V3), U10.1 (+3V3), U10.6 (+3V3), U11.1 (+3V3), U11.2 (+3V3), U11.6 (+3V3), U14.1 (+3V3), U14.6 (+3V3), U17.1 (+3V3), U17.6 (+3V3), U26.14 (+3V3), U27.21 (A0), U27.24 (VDD), U28.3 (A2), U28.24 (VDD), U30.5 (+3V3), U35.5 (+3V3), U36.5 (+3V3), U37.5 (+3V3), U38.5 (+3V3)
+5V_D8: J_MEZZ_PWR1.1, U23.5 (+5V_D8)
+5V_DEV: C49.1, C50.1, C51.1, C103.1, C155.1, C167.1, C168.1, C169.1, J_5V_DEV.1, R40.1, R43.2, R100.1, R183.1, R188.1, U7.12 (+5V_DEV), U11.8 (+5V_DEV), U11.9 (+5V_DEV), U18.17 (+5V_DEV), U23.4 (+5V_DEV), U32.4 (+5V_DEV)
+5V_S1: C31.1, C32.1, C33.1, J_5V_S1.1, R28.1, R31.2, U8.8 (+5V_S1), U8.9 (+5V_S1)
+5V_S2: C37.1, C38.1, C39.1, C164.1, C165.1, C166.1, J_5V_S2.1, R32.1, R35.2, R176.1, U5.12 (+5V_S2), U9.8 (+5V_S2), U9.9 (+5V_S2)
+5V_S3: C43.1, C44.1, C45.1, J_5V_S3.1, R36.1, R39.2, U10.8 (+5V_S3), U10.9 (+5V_S3)
+12V_HF: C109.1, C110.1, C111.1, C172.1, C173.1, C196.1, J_HF.1, R60.1, R65.2, R165.1, U15.12 (+12V_HF), U15.24 (+12V_HF)
+13V8_PA: C65.1, C66.1, C67.1, C170.1, C171.1, C195.1, J_PA.1, R50.1, R55.2, R163.1, U13.12 (+13V8_PA), U13.24 (+13V8_PA), U14.8 (+13V8_PA), U14.9 (+13V8_PA)
+54V_POE: C83.1, C84.1, C85.1, C176.1, C177.1, J_54V.1, R66.1, R71.2, R167.1, U16.12 (+54V_POE), U17.9 (+54V_POE)
AB_SPARE: J_MEZZ1.16, TP27.1
B33_BST: C52.1, U12.6 (B33_BST)
B33_FB: R48.2, R49.1, U12.8 (B33_FB)
B33_SS: C53.1, U12.7 (B33_SS)
B33_SW: C52.2, L7.1, U12.5 (B33_SW)
CELL+: F1.1, J_CP1.1, J_CP2.1, J_CP3.1, J_CP4.1, R1.2, TP14.1
CELL_FUSED: C1.1, C2.1, C3.1, F1.2, R17.2, R148.1
CHG_ILIM: Q6.3 (D), R19.2, R20.1, U3.6 (CHG_ILIM)
CHG_INHIBIT: Q6.1 (G), R21.1, U27.4 (IO0_0)
CHRG_OK: R22.1, U3.4 (CHRG_OK), U27.13 (IO1_0)
CH_ACN: C190.1, C191.1, Q7.5 (CH_ACN), R16.2, R146.1
CH_ACN_F: C121.2, R146.2, U3.2 (CH_ACN_F)
CH_ACP_F: C121.1, R147.2, U3.3 (CH_ACP_F)
CH_BTST1: C16.1, U3.30 (CH_BTST1)
CH_BTST2: C17.1, U3.25 (CH_BTST2)
CH_CELL: R26.2, R27.1, U3.18 (CH_CELL)
CH_COMP1: R25.1, U3.16 (CH_COMP1)
CH_COMP1C: C26.1, R25.2
CH_COMP2: C27.1, U3.17 (CH_COMP2)
CH_HIDRV1: Q7.4 (CH_HIDRV1), U3.31 (CH_HIDRV1)
CH_HIDRV2: Q10.4 (CH_HIDRV2), U3.24 (CH_HIDRV2)
CH_LODRV1: Q8.4 (CH_LODRV1), U3.29 (CH_LODRV1)
CH_LODRV2: Q9.4 (CH_LODRV2), U3.26 (CH_LODRV2)
CH_SRN_F: C122.2, R148.2, U3.19 (CH_SRN_F)
CH_SRP_F: C122.1, R149.2, U3.20 (CH_SRP_F)
CH_SW1: C16.2, L2.1, Q7.1 (CH_SW1), Q7.2 (CH_SW1), Q7.3 (CH_SW1), Q8.5 (CH_SW1), U3.32 (CH_SW1)
CH_SW2: C17.2, L2.2, Q9.5 (CH_SW2), Q10.1 (CH_SW2), Q10.2 (CH_SW2), Q10.3 (CH_SW2), U3.23 (CH_SW2)
CH_VDDA: C19.1, R18.2, R26.1, U3.7 (CH_VDDA)
D8_EN: R113.1, U23.3 (D8_EN), U27.7 (IO0_3)
D8_FLT: R99.1, U23.6 (D8_FLT), U27.17 (IO1_4)
DEV_EN: R42.1, U7.1 (DEV_EN), U27.11 (IO0_7)
DOCK_SPARE: J_DOCK.12, TP21.1, U27.18 (IO1_5)
EMCON_HW: J_AB1.15, R102.1, TP15.1, U35.2 (EMCON_HW), U37.2 (EMCON_HW)
EXP2_SP3: TP3.1, U28.15 (IO1_2)
EXP2_SP4: TP4.1, U28.16 (IO1_3)
EXP2_SP5: TP5.1, U28.17 (IO1_4)
EXP2_SP6: TP6.1, U28.18 (IO1_5)
EXP2_SP7: TP7.1, U28.19 (IO1_6)
EXP2_SP8: TP8.1, U28.20 (IO1_7)
EXP2_SPC: TP25.1, U28.6 (IO0_2)
EXP2_SPD: TP26.1, U28.7 (IO0_3)
EXP_INT: J_AB1.13, J_MEZZ1.12, R110.1, U27.1 (~INT), U28.1 (~INT)
FE_BLEED: Q38.5 (FE_BLEED), R202.2, R203.2, R204.2, R205.2
FE_BLEED_G: Q37.3 (D), Q38.4 (FE_BLEED_G), R201.2
FE_BOOT1: C9.1, D9.1 (K), U2.26 (FE_BOOT1)
FE_BOOT2: C10.1, D10.1 (K), U2.20 (FE_BOOT2)
FE_COMP: C6.1, R10.1, U2.9 (FE_COMP)
FE_COMPC: C5.1, R10.2
FE_CS: Q3.1 (FE_CS), Q3.2 (FE_CS), Q3.3 (FE_CS), Q4.1 (FE_CS), Q4.2 (FE_CS), Q4.3 (FE_CS), R12.1, R150.1
FE_CSF: C123.1, R150.2, U2.16 (FE_CSF)
FE_CSGF: C123.2, R151.2, U2.15 (FE_CSGF)
FE_CTR2: C212.1, U34.9 (FE_CTR2)
FE_EN: C213.1, R199.2, R206.1, U2.1 (FE_EN)
FE_FB: R6.2, R7.1, U2.11 (FE_FB)
FE_GVDD: C210.1, R196.2, U34.1 (FE_GVDD)
FE_HDRV1: Q2.4 (FE_HDRV1), U2.27 (FE_HDRV1)
FE_HDRV2: Q5.4 (FE_HDRV2), U2.19 (FE_HDRV2)
FE_ISNS_N: C128.2, R161.2, U2.13 (FE_ISNS_N)
FE_ISNS_P: C128.1, R160.2, U2.14 (FE_ISNS_P)
FE_LATCH: Q36.3 (D), R197.2, U34.2 (FE_LATCH)
FE_LDRV1: Q3.4 (FE_LDRV1), U2.25 (FE_LDRV1)
FE_LDRV2: Q4.4 (FE_LDRV2), U2.21 (FE_LDRV2)
FE_MODE: R119.1, U2.4 (FE_MODE)
FE_OUT: C13.1, C14.1, C15.1, Q5.5 (FE_OUT), R11.1, R160.1
FE_PGOOD: R13.1, U2.17 (FE_PGOOD), U27.20 (IO1_7)
FE_RT: R8.1, U2.6 (FE_RT)
FE_RUN: Q36.1 (G), Q37.1 (G), R198.2, R199.1, U34.4 (FE_RUN), U34.5 (FE_RUN)
FE_SLOPE: C147.1, U2.7 (FE_SLOPE)
FE_SS: C7.1, U2.8 (FE_SS)
FE_SW1: C9.2, L1.1, Q2.1 (FE_SW1), Q2.2 (FE_SW1), Q2.3 (FE_SW1), Q3.5 (FE_SW1), U2.28 (FE_SW1)
FE_SW2: C10.2, L1.2, Q4.5 (FE_SW2), Q5.1 (FE_SW2), Q5.2 (FE_SW2), Q5.3 (FE_SW2), U2.18 (FE_SW2)
FE_UVS: C211.1, R14.2, R15.1, U34.3 (FE_UVS)
FE_VCC: C8.1, D9.2 (A), D10.2 (A), R119.2, U2.23 (FE_VCC)
FE_VINP: C207.1, D19.1 (K), U2.2 (FE_VINP)
FE_VISNS: R195.2, U2.3 (FE_VISNS)
FE_VZ: C214.1, D22.1 (K), R198.1, R200.2, R201.1
GND: C1.2, C2.2, C3.2, C4.2, C5.2, C6.2, C7.2, C8.2, C11.2, C12.2, C13.2, C14.2, C15.2, C18.2, C19.2, C20.2, C21.2, C22.2, C23.2, C24.2, C25.2, C26.2, C27.2, C29.2, C30.2, C31.2, C32.2, C33.2, C35.2, C36.2, C37.2, C38.2, C39.2, C41.2, C42.2, C43.2, C44.2, C45.2, C47.2, C48.2, C49.2, C50.2, C51.2, C53.2, C54.2, C55.2, C56.2, C57.2, C58.2, C59.2, C60.2, C63.2, C64.2, C65.2, C66.2, C67.2, C68.2, C69.2, C70.2, C71.2, C74.2, C75.2, C76.2, C77.2, C78.2, C81.2, C82.2, C83.2, C84.2, C85.2, C86.2, C87.2, C88.2, C89.2, C92.2, C93.2, C94.2, C95.2, C96.2, C97.2, C98.2, C99.2, C100.2, C101.2, C102.2, C103.2, C104.2, C106.2, C107.2, C108.2, C109.2, C110.2, C111.2, C112.2, C113.2, C114.2, C115.2, C116.2, C117.2, C118.2, C119.2, C120.2, C133.2, C134.2, C135.2, C136.2, C140.2, C141.2, C142.2, C143.2, C147.2, C148.2, C149.2, C150.2, C151.2, C152.2, C153.2, C154.2, C155.2, C156.2, C158.2, C159.2, C160.2, C161.2, C162.2, C163.2, C164.2, C165.2, C166.2, C167.2, C168.2, C169.2, C170.2, C171.2, C172.2, C173.2, C174.2, C175.2, C176.2, C177.2, C178.2, C179.2, C180.2, C181.2, C182.2, C183.2, C184.2, C185.2, C186.2, C187.2, C188.2, C189.2, C190.2, C191.2, C192.2, C193.2, C194.2, C195.2, C196.2, C197.2, C198.2, C199.2, C200.2, C201.2, C202.2, C203.2, C204.2, C205.2, C206.2, C207.2, C208.2, C209.2, C210.2, C211.2, C212.2, C213.2, C214.2, C215.2, C216.2, C217.2, C218.2, C219.2, C220.2, C221.2, C222.2, C223.2, D1.2 (A), D2.2 (A), D3.2 (A), D4.2 (A), D22.2 (A), J_5V_DEV.2, J_5V_S1.2, J_5V_S2.2, J_5V_S3.2, J_54V.2, J_AB1.3, J_AB1.4, J_AB1.5, J_AB1.6, J_AB1.7, J_AB1.8, J_AB1.22, J_AB1.23, J_AB1.24, J_AB2.3, J_AB2.4, J_AB2.5, J_AB2.6, J_AB2.7, J_AB2.8, J_AB2.9, J_AB2.10, J_BM1.2 (Ext), J_BM2.2 (Ext), J_BM3.2 (Ext), J_BM4.2 (Ext), J_BM5.2 (Ext), J_BM6.2 (Ext), J_BM7.2 (Ext), J_BM8.2 (Ext), J_BM9.2 (Ext), J_BM10.2 (Ext), J_BM11.2 (Ext), J_CN1.1, J_CN2.1, J_CN3.1, J_CN4.1, J_DOCK.5, J_DOCK.6, J_DOCK.7, J_DOCK.11, J_HEAT.2, J_HF.2, J_MAINSW.2, J_MEZZ1.3, J_MEZZ1.4, J_MEZZ1.5, J_MEZZ1.6, J_MEZZ1.14, J_MEZZ_PWR1.2, J_MON.2, J_PA.2, J_RF1.2 (Ext), J_RF2.2 (Ext), J_RF3.2 (Ext), J_RF4.2 (Ext), J_RF5.2 (Ext), J_RF6.2 (Ext), J_RF7.2 (Ext), J_RF8.2 (Ext), J_RF9.2 (Ext), J_RF10.2 (Ext), J_RF11.2 (Ext), J_USBC_OUT.4, J_USBC_OUT.5, J_USBW.4, Q1.2 (S), Q6.2 (S), Q8.1 (GND), Q8.2 (GND), Q8.3 (GND), Q9.1 (GND), Q9.2 (GND), Q9.3 (GND), Q36.2 (S), Q37.2 (S), Q38.1 (GND), Q38.2 (GND), Q38.3 (GND), R5.2, R7.2, R8.2, R12.2, R15.2, R20.2, R21.2, R24.2, R27.2, R29.2, R30.2, R33.2, R34.2, R37.2, R38.2, R41.2, R45.2, R46.2, R47.2, R49.2, R51.2, R52.2, R56.2, R59.2, R61.2, R62.2, R67.2, R68.2, R72.2, R75.2, R77.2, R78.2, R90.2, R93.2, R94.2, R97.2, R98.2, R101.2, R102.2, R103.2, R104.2, R111.2, R112.2, R113.2, R114.2, R115.2, R116.2, R118.2, R122.2, R125.2, R127.2, R134.2, R141.2, R143.2, R145.2, R151.1, R153.1, R155.1, R157.1, R159.1, R170.2, R174.1, R177.2, R181.1, R184.2, R186.2, R189.2, R190.2, R192.2, R194.2, R206.2, R207.2, R208.2, TP10.1, U1.4 (GND), U2.5 (GND), U2.10 (GND), U2.22 (GND), U2.29 (GND), U3.5 (GND), U3.14 (GND), U3.27 (GND), U3.33 (GND), U4.7 (GND), U4.9 (GND), U5.5 (GND), U5.10 (GND), U5.22 (GND), U5.29 (GND), U6.7 (GND), U6.9 (GND), U7.5 (GND), U7.10 (GND), U7.22 (GND), U7.29 (GND), U8.1 (GND), U8.2 (GND), U8.7 (GND), U9.1 (GND), U9.7 (GND), U10.2 (GND), U10.7 (GND), U11.7 (GND), U12.4 (GND), U13.5 (GND), U13.10 (GND), U13.22 (GND), U13.29 (GND), U14.7 (GND), U15.5 (GND), U15.10 (GND), U15.22 (GND), U15.29 (GND), U16.5 (GND), U16.10 (GND), U16.22 (GND), U16.29 (GND), U17.7 (GND), U18.4 (GND), U18.9 (GND), U18.10 (GND), U18.18 (GND), U18.25 (GND), U19.5 (GND), U19.10 (GND), U19.22 (GND), U19.29 (GND), U21.1 (GND), U21.9 (GND), U22.1 (GND), U22.9 (GND), U23.1 (GND), U23.9 (GND), U26.1 (GND), U26.2 (GND), U26.4 (GND), U26.5 (GND), U26.7 (GND), U27.2 (A1), U27.3 (A2), U27.12 (VSS), U28.2 (A1), U28.12 (VSS), U28.21 (A0), U29.2 (GND), U30.3 (GND), U31.3 (GND), U32.1 (GND), U32.9 (GND), U33.4 (GND), U34.10 (GND), U34.11 (GND), U35.3 (GND), U36.3 (GND), U37.3 (GND), U38.3 (GND)
HEAT_EN: R112.1, U22.3 (HEAT_EN), U27.6 (IO0_2)
HEAT_FLT: R95.1, U22.6 (HEAT_FLT), U27.16 (IO1_3)
HF_BOOT1: C72.1, D13.1 (K), U15.26 (HF_BOOT1)
HF_BOOT2: C73.1, D14.1 (K), U15.20 (HF_BOOT2)
HF_COMP: C69.1, R64.1, U15.9 (HF_COMP)
HF_COMPC: C68.1, R64.2
HF_CS: Q16.1 (HF_CS), Q16.2 (HF_CS), Q16.3 (HF_CS), Q23.1 (HF_CS), Q23.2 (HF_CS), Q23.3 (HF_CS), R122.1, R154.1
HF_CSF: C125.1, R154.2, U15.16 (HF_CSF)
HF_CSGF: C125.2, R155.2, U15.15 (HF_CSGF)
HF_EN: R124.1, U38.4 (HF_EN)
HF_FB: R60.2, R61.1, U15.11 (HF_FB)
HF_HDRV1: Q15.4 (HF_HDRV1), U15.27 (HF_HDRV1)
HF_HDRV2: Q24.4 (HF_HDRV2), U15.19 (HF_HDRV2)
HF_ISNS_N: C130.2, R165.2, U15.13 (HF_ISNS_N)
HF_ISNS_P: C130.1, R164.2, U15.14 (HF_ISNS_P)
HF_LDRV1: Q16.4 (HF_LDRV1), U15.25 (HF_LDRV1)
HF_LDRV2: Q23.4 (HF_LDRV2), U15.21 (HF_LDRV2)
HF_MODE: R126.1, U15.4 (HF_MODE)
HF_OUT: Q24.5 (HF_OUT), R65.1, R164.1
HF_PGOOD: R123.1, U15.17 (HF_PGOOD), U28.10 (IO0_6)
HF_RT: R62.1, U15.6 (HF_RT)
HF_SLOPE: C149.1, U15.7 (HF_SLOPE)
HF_SS: C70.1, U15.8 (HF_SS)
HF_SW1: C72.2, L9.1, Q15.1 (HF_SW1), Q15.2 (HF_SW1), Q15.3 (HF_SW1), Q16.5 (HF_SW1), U15.28 (HF_SW1)
HF_SW2: C73.2, L9.2, Q23.5 (HF_SW2), Q24.1 (HF_SW2), Q24.2 (HF_SW2), Q24.3 (HF_SW2), U15.18 (HF_SW2)
HF_SW_EN: R104.1, U27.10 (IO0_6), U38.2 (HF_SW_EN)
HF_TXOK: R208.1, U37.4 (HF_TXOK), U38.1 (HF_TXOK)
HF_UVLO: R124.2, R125.1, U15.1 (HF_UVLO)
HF_VCC: C71.1, D13.2 (A), D14.2 (A), R126.2, U15.23 (HF_VCC)
HF_VINP: C209.1, D21.1 (K), U15.2 (HF_VINP)
HT_BST: C157.1, U33.6 (HT_BST)
HT_EN: R193.2, R194.1, U33.2 (HT_EN)
HT_FB: R191.2, R192.1, U33.8 (HT_FB)
HT_SS: C158.1, U33.7 (HT_SS)
HT_SW: C157.2, L12.1, U33.5 (HT_SW)
IADPT: TP19.1, U3.8 (IADPT)
IBAT: TP20.1, U3.9 (IBAT)
INA_ALERT: R44.1, U8.3 (INA_ALERT), U9.3 (INA_ALERT), U10.3 (INA_ALERT), U11.3 (INA_ALERT), U14.3 (INA_ALERT), U17.3 (INA_ALERT), U27.19 (IO1_6)
KILL: Q1.3 (D), R4.1, U1.8 (KILL)
MAIN_PB: J_MAINSW.1, U1.2 (MAIN_PB)
MAIN_PDT: C152.1, U1.7 (MAIN_PDT)
MON_EN: R111.1, U21.3 (MON_EN), U27.5 (IO0_1)
MON_FLT: R91.1, U21.6 (MON_FLT), U27.15 (IO1_2)
OUTLET_OK: U26.10 (OUTLET_OK), U26.13 (OUTLET_OK), U30.4 (OUTLET_OK)
PA_BOOT1: C61.1, D11.1 (K), U13.26 (PA_BOOT1)
PA_BOOT2: C62.1, D12.1 (K), U13.20 (PA_BOOT2)
PA_COMP: C58.1, R54.1, U13.9 (PA_COMP)
PA_COMPC: C57.1, R54.2
PA_CS: Q12.1 (PA_CS), Q12.2 (PA_CS), Q12.3 (PA_CS), Q13.1 (PA_CS), Q13.2 (PA_CS), Q13.3 (PA_CS), R56.1, R152.1
PA_CSF: C124.1, R152.2, U13.16 (PA_CSF)
PA_CSGF: C124.2, R153.2, U13.15 (PA_CSGF)
PA_EN: J_MEZZ1.9, R58.1, U30.2 (PA_EN), U36.4 (PA_EN)
PA_FB: R50.2, R51.1, U13.11 (PA_FB)
PA_HDRV1: Q11.4 (PA_HDRV1), U13.27 (PA_HDRV1)
PA_HDRV2: Q14.4 (PA_HDRV2), U13.19 (PA_HDRV2)
PA_ISNS_N: C129.2, R163.2, U13.13 (PA_ISNS_N)
PA_ISNS_P: C129.1, R162.2, U13.14 (PA_ISNS_P)
PA_LDRV1: Q12.4 (PA_LDRV1), U13.25 (PA_LDRV1)
PA_LDRV2: Q13.4 (PA_LDRV2), U13.21 (PA_LDRV2)
PA_MODE: R120.1, U13.4 (PA_MODE)
PA_OUT: Q14.5 (PA_OUT), R55.1, R162.1, U14.10 (PA_OUT)
PA_PGOOD: R57.1, U13.17 (PA_PGOOD), U28.8 (IO0_4)
PA_RT: R52.1, U13.6 (PA_RT)
PA_SLOPE: C148.1, U13.7 (PA_SLOPE)
PA_SS: C59.1, U13.8 (PA_SS)
PA_SW1: C61.2, L8.1, Q11.1 (PA_SW1), Q11.2 (PA_SW1), Q11.3 (PA_SW1), Q12.5 (PA_SW1), U13.28 (PA_SW1)
PA_SW2: C62.2, L8.2, Q13.5 (PA_SW2), Q14.1 (PA_SW2), Q14.2 (PA_SW2), Q14.3 (PA_SW2), U13.18 (PA_SW2)
PA_SW_EN: R103.1, U27.9 (IO0_5), U36.2 (PA_SW_EN)
PA_TXOK: R207.1, U35.4 (PA_TXOK), U36.1 (PA_TXOK)
PA_UVLO: R58.2, R59.1, U13.1 (PA_UVLO)
PA_VCC: C60.1, D11.2 (A), D12.2 (A), R120.2, U13.23 (PA_VCC)
PA_VINP: C208.1, D20.1 (K), U13.2 (PA_VINP)
PD_BOOT1: C90.1, D17.1 (K), U19.26 (PD_BOOT1)
PD_BOOT2: C91.1, D18.1 (K), U19.20 (PD_BOOT2)
PD_CC1: C96.1, J_USBC_OUT.2, U18.2 (PD_CC1), U31.1 (PD_CC1)
PD_CC2: C97.1, J_USBC_OUT.3, U18.3 (PD_CC2), U31.2 (PD_CC2)
PD_COMP: C87.1, R80.1, U19.9 (PD_COMP)
PD_COMPC: C86.1, R80.2
PD_CS: Q22.1 (PD_CS), Q22.2 (PD_CS), Q22.3 (PD_CS), Q25.1 (PD_CS), Q25.2 (PD_CS), Q25.3 (PD_CS), R127.1, R158.1
PD_CSF: C127.1, R158.2, U19.16 (PD_CSF)
PD_CSGF: C127.2, R159.2, U19.15 (PD_CSGF)
PD_CTL1: R137.2, U18.6 (PD_CTL1)
PD_CTL2: R136.2, U18.7 (PD_CTL2)
PD_DSCG: R139.1, U18.24 (PD_DSCG)
PD_DVDD: C94.1, U18.5 (PD_DVDD), U18.8 (PD_DVDD), U18.12 (PD_DVDD), U18.13 (PD_DVDD)
PD_EN: R133.1, R133.2, R134.1, U19.1 (PD_EN), U26.11 (PD_EN)
PD_FB: R76.2, R77.1, R136.1, R137.1, U19.11 (PD_FB)
PD_GD: R140.2, R141.1, U18.15 (PD_GD)
PD_GDNG: Q27.4 (PD_GDNG), U18.22 (PD_GDNG)
PD_HDRV1: Q21.4 (PD_HDRV1), U19.27 (PD_HDRV1)
PD_HDRV2: Q26.4 (PD_HDRV2), U19.19 (PD_HDRV2)
PD_ISNS_N: C132.2, R169.2, U19.13 (PD_ISNS_N)
PD_ISNS_P: C132.1, R168.2, U19.14 (PD_ISNS_P)
PD_LDRV1: Q22.4 (PD_LDRV1), U19.25 (PD_LDRV1)
PD_LDRV2: Q25.4 (PD_LDRV2), U19.21 (PD_LDRV2)
PD_MODE: R135.1, U19.4 (PD_MODE)
PD_OUT: Q26.5 (PD_OUT), R81.1, R168.1
PD_PGOOD: R128.1, U19.17 (PD_PGOOD), U28.11 (IO0_7)
PD_RT: R78.1, U19.6 (PD_RT)
PD_SLOPE: C151.1, U19.7 (PD_SLOPE)
PD_SS: C88.1, U19.8 (PD_SS)
PD_SW: Q27.1 (PD_SW), Q27.2 (PD_SW), Q27.3 (PD_SW), R138.1, U18.19 (PD_SW), U18.23 (PD_SW)
PD_SW1: C90.2, L11.1, Q21.1 (PD_SW1), Q21.2 (PD_SW1), Q21.3 (PD_SW1), Q22.5 (PD_SW1), U19.28 (PD_SW1)
PD_SW2: C91.2, L11.2, Q25.5 (PD_SW2), Q26.1 (PD_SW2), Q26.2 (PD_SW2), Q26.3 (PD_SW2), U19.18 (PD_SW2)
PD_SW_EN: R143.1, U26.12 (PD_SW_EN), U28.13 (IO1_0)
PD_UFP: R142.1, U18.11 (PD_UFP), U28.14 (IO1_1)
PD_VAUX: C95.1, U18.14 (PD_VAUX), U18.16 (PD_VAUX)
PD_VBUS: C120.1, D4.1 (K), J_USBC_OUT.1, R138.2, R139.2, U18.21 (PD_VBUS)
PD_VCC: C89.1, D17.2 (A), D18.2 (A), R135.2, U19.23 (PD_VCC)
PD_VPWR: C117.1, C118.1, C119.1, C174.1, C175.1, Q27.5 (PD_VPWR), R76.1, R81.2, R140.1, R169.1, U18.20 (PD_VPWR), U19.12 (PD_VPWR)
PD_VTX: C93.1, U18.1 (PD_VTX)
PI_KILL: J_AB1.10, Q1.1 (G), R5.1
PI_SHDN_REQ: J_AB1.9, R3.1, U1.5 (PI_SHDN_REQ)
POE_BOOT1: C79.1, D15.1 (K), U16.26 (POE_BOOT1)
POE_BOOT2: C80.1, D16.1 (K), U16.20 (POE_BOOT2)
POE_COMP: C76.1, R70.1, U16.9 (POE_COMP)
POE_COMPC: C75.1, R70.2
POE_CS: Q18.1 (POE_CS), Q18.2 (POE_CS), Q18.3 (POE_CS), Q19.1 (POE_CS), Q19.2 (POE_CS), Q19.3 (POE_CS), R72.1, R156.1
POE_CSF: C126.1, R156.2, U16.16 (POE_CSF)
POE_CSGF: C126.2, R157.2, U16.15 (POE_CSGF)
POE_EN: R74.1, R74.2, R75.1, U16.1 (POE_EN), U26.8 (POE_EN)
POE_FB: R66.2, R67.1, U16.11 (POE_FB)
POE_HDRV1: Q17.4 (POE_HDRV1), U16.27 (POE_HDRV1)
POE_HDRV2: Q20.4 (POE_HDRV2), U16.19 (POE_HDRV2)
POE_ISNS_N: C131.2, R167.2, U16.13 (POE_ISNS_N)
POE_ISNS_P: C131.1, R166.2, U16.14 (POE_ISNS_P)
POE_LDRV1: Q18.4 (POE_LDRV1), U16.25 (POE_LDRV1)
POE_LDRV2: Q19.4 (POE_LDRV2), U16.21 (POE_LDRV2)
POE_MODE: R121.1, U16.4 (POE_MODE)
POE_OUT: Q20.5 (POE_OUT), R71.1, R166.1, U17.10 (POE_OUT)
POE_PGOOD: R73.1, U16.17 (POE_PGOOD), U28.9 (IO0_5)
POE_RT: R68.1, U16.6 (POE_RT)
POE_SLOPE: C150.1, U16.7 (POE_SLOPE)
POE_SS: C77.1, U16.8 (POE_SS)
POE_SW1: C79.2, L10.1, Q17.1 (POE_SW1), Q17.2 (POE_SW1), Q17.3 (POE_SW1), Q18.5 (POE_SW1), U16.28 (POE_SW1)
POE_SW2: C80.2, L10.2, Q19.5 (POE_SW2), Q20.1 (POE_SW2), Q20.2 (POE_SW2), Q20.3 (POE_SW2), U16.18 (POE_SW2)
POE_SW_EN: R114.1, U26.9 (POE_SW_EN), U27.8 (IO0_4)
POE_VCC: C78.1, D15.2 (A), D16.2 (A), R121.2, U16.23 (POE_VCC)
PRECHG: J_PRE1.1, R1.1
PROCHOT: R23.1, U3.11 (PROCHOT), U27.14 (IO1_1)
PSYS: R24.1, U3.10 (PSYS)
RAIL_EN: R2.1, R184.1, TP16.1, U1.6 (RAIL_EN), U12.2 (RAIL_EN)
REGN: C18.1, R18.1, R19.1, TP22.1, U3.28 (REGN)
RF_5G1: J_BM8.1 (In), J_RF8.1 (In)
RF_5G2: J_BM9.1 (In), J_RF9.1 (In)
RF_GNSS: J_BM4.1 (In), J_RF4.1 (In)
RF_HF: J_BM2.1 (In), J_RF2.1 (In)
RF_IRIDIUM: J_BM10.1 (In), J_RF10.1 (In)
RF_LORA: J_BM11.1 (In), J_RF11.1 (In)
RF_P2PA: J_BM6.1 (In), J_RF6.1 (In)
RF_P2PB: J_BM7.1 (In), J_RF7.1 (In)
RF_SDR: J_BM5.1 (In), J_RF5.1 (In)
RF_VHF: J_BM1.1 (In), J_RF1.1 (In)
RF_WIFI24: J_BM3.1 (In), J_RF3.1 (In)
S1_BOOT: C28.1, U4.1 (S1_BOOT)
S1_COMP: R129.1, U4.6 (S1_COMP)
S1_COMPC: C112.1, R129.2
S1_FB: R28.2, R29.1, U4.5 (S1_FB)
S1_OUT: L3.2, R31.1, U8.10 (S1_OUT)
S1_RT: R45.1, U4.4 (S1_RT)
S1_SW: C28.2, L3.1, U4.8 (S1_SW)
S2_BOOT1: C34.1, D5.1 (K), U5.26 (S2_BOOT1)
S2_BOOT2: C137.1, D6.1 (K), U5.20 (S2_BOOT2)
S2_COMP: C134.1, R130.1, U5.9 (S2_COMP)
S2_COMPC: C113.1, R130.2
S2_CS: Q29.1 (S2_CS), Q29.2 (S2_CS), Q29.3 (S2_CS), Q30.1 (S2_CS), Q30.2 (S2_CS), Q30.3 (S2_CS), R170.1, R173.1
S2_CSF: C138.1, R173.2, U5.16 (S2_CSF)
S2_CSGF: C138.2, R174.2, U5.15 (S2_CSGF)
S2_FB: R32.2, R33.1, U5.11 (S2_FB)
S2_HDRV1: Q28.4 (S2_HDRV1), U5.27 (S2_HDRV1)
S2_HDRV2: Q31.4 (S2_HDRV2), U5.19 (S2_HDRV2)
S2_ISNS_N: C139.2, R176.2, U5.13 (S2_ISNS_N)
S2_ISNS_P: C139.1, R175.2, U5.14 (S2_ISNS_P)
S2_LDRV1: Q29.4 (S2_LDRV1), U5.25 (S2_LDRV1)
S2_LDRV2: Q30.4 (S2_LDRV2), U5.21 (S2_LDRV2)
S2_MODE: R172.1, U5.4 (S2_MODE)
S2_OUT: Q31.5 (S2_OUT), R35.1, R175.1, U9.10 (S2_OUT)
S2_PGOOD: R171.1, U5.17 (S2_PGOOD)
S2_RT: R46.1, U5.6 (S2_RT)
S2_SLOPE: C133.1, U5.7 (S2_SLOPE)
S2_SS: C135.1, U5.8 (S2_SS)
S2_SW1: C34.2, L4.1, Q28.1 (S2_SW1), Q28.2 (S2_SW1), Q28.3 (S2_SW1), Q29.5 (S2_SW1), U5.28 (S2_SW1)
S2_SW2: C137.2, L4.2, Q30.5 (S2_SW2), Q31.1 (S2_SW2), Q31.2 (S2_SW2), Q31.3 (S2_SW2), U5.18 (S2_SW2)
S2_VCC: C136.1, D5.2 (A), D6.2 (A), R172.2, U5.23 (S2_VCC)
S3_BOOT: C40.1, U6.1 (S3_BOOT)
S3_COMP: R131.1, U6.6 (S3_COMP)
S3_COMPC: C114.1, R131.2
S3_FB: R36.2, R37.1, U6.5 (S3_FB)
S3_OUT: L5.2, R39.1, U10.10 (S3_OUT)
S3_RT: R47.1, U6.4 (S3_RT)
S3_SW: C40.2, L5.1, U6.8 (S3_SW)
SCL: J_AB1.12, J_MEZZ1.11, TP18.1, U3.13 (SCL), U8.5 (SCL), U9.5 (SCL), U10.5 (SCL), U11.5 (SCL), U14.5 (SCL), U17.2 (SCL), U17.5 (SCL), U27.22 (SCL), U28.22 (SCL)
SDA: J_AB1.11, J_MEZZ1.10, TP17.1, U3.12 (SDA), U8.4 (SDA), U9.4 (SDA), U10.4 (SDA), U11.4 (SDA), U14.2 (SDA), U14.4 (SDA), U17.4 (SDA), U27.23 (SDA), U28.23 (SDA)
SD_BOOT1: C46.1, D7.1 (K), U7.26 (SD_BOOT1)
SD_BOOT2: C144.1, D8.1 (K), U7.20 (SD_BOOT2)
SD_COMP: C141.1, R132.1, U7.9 (SD_COMP)
SD_COMPC: C115.1, R132.2
SD_CS: Q33.1 (SD_CS), Q33.2 (SD_CS), Q33.3 (SD_CS), Q34.1 (SD_CS), Q34.2 (SD_CS), Q34.3 (SD_CS), R177.1, R180.1
SD_CSF: C145.1, R180.2, U7.16 (SD_CSF)
SD_CSGF: C145.2, R181.2, U7.15 (SD_CSGF)
SD_FB: R40.2, R41.1, U7.11 (SD_FB)
SD_HDRV1: Q32.4 (SD_HDRV1), U7.27 (SD_HDRV1)
SD_HDRV2: Q35.4 (SD_HDRV2), U7.19 (SD_HDRV2)
SD_ISNS_N: C146.2, R183.2, U7.13 (SD_ISNS_N)
SD_ISNS_P: C146.1, R182.2, U7.14 (SD_ISNS_P)
SD_LDRV1: Q33.4 (SD_LDRV1), U7.25 (SD_LDRV1)
SD_LDRV2: Q34.4 (SD_LDRV2), U7.21 (SD_LDRV2)
SD_MODE: R179.1, U7.4 (SD_MODE)
SD_OUT: Q35.5 (SD_OUT), R43.1, R182.1, U11.10 (SD_OUT)
SD_PGOOD: R178.1, U7.17 (SD_PGOOD)
SD_RT: R115.1, U7.6 (SD_RT)
SD_SLOPE: C140.1, U7.7 (SD_SLOPE)
SD_SS: C142.1, U7.8 (SD_SS)
SD_SW1: C46.2, L6.1, Q32.1 (SD_SW1), Q32.2 (SD_SW1), Q32.3 (SD_SW1), Q33.5 (SD_SW1), U7.28 (SD_SW1)
SD_SW2: C144.2, L6.2, Q34.5 (SD_SW2), Q35.1 (SD_SW2), Q35.2 (SD_SW2), Q35.3 (SD_SW2), U7.18 (SD_SW2)
SD_VCC: C143.1, D7.2 (A), D8.2 (A), R179.2, U7.23 (SD_VCC)
SHORE_INHIBIT: J_AB1.21, J_DOCK.8, R118.1
SLOT_EN1: J_AB1.17, R30.1, U4.3 (SLOT_EN1)
SLOT_EN2: J_AB1.18, R34.1, U5.1 (SLOT_EN2)
SLOT_EN3: J_AB1.19, R38.1, U6.3 (SLOT_EN3)
TR_APRS: J_AB1.14, J_MEZZ1.7, R116.1, U30.1 (TR_APRS)
TX_INHIBIT_n: J_AB1.16, J_MEZZ1.8, R145.1, U35.1 (TX_INHIBIT_n), U37.1 (TX_INHIBIT_n)
U21_DVDT: C98.1, U21.2 (U21_DVDT)
U21_ILM: R90.1, U21.7 (U21_ILM)
U21_OVLO: R92.2, R93.1, U21.8 (U21_OVLO)
U22_DVDT: C100.1, U22.2 (U22_DVDT)
U22_ILM: R94.1, U22.7 (U22_ILM)
U22_OVLO: R96.2, R97.1, U22.8 (U22_OVLO)
U23_DVDT: C102.1, U23.2 (U23_DVDT)
U23_ILM: R98.1, U23.7 (U23_ILM)
U23_OVLO: R100.2, R101.1, U23.8 (U23_OVLO)
U32_DVDT: C154.1, U32.2 (U32_DVDT)
U32_ILM: R186.1, U32.7 (U32_ILM)
U32_OVLO: R188.2, R189.1, U32.8 (U32_OVLO)
USBX_EN: R190.1, TP23.1, U28.4 (IO0_0), U32.3 (USBX_EN)
USBX_FLT: R187.1, TP24.1, U28.5 (IO0_1), U32.6 (USBX_FLT)
USB_D8_N: J_AB1.2, J_MEZZ1.2
USB_D8_P: J_AB1.1, J_MEZZ1.1
USB_E6_N: J_AB1.26, J_DOCK.10
USB_E6_P: J_AB1.25, J_DOCK.9
USB_WALL_N: J_AB2.2, J_USBW.2, U29.3 (I/O2), U29.4 (I/O2)
USB_WALL_P: J_AB2.1, J_USBW.3, U29.1 (I/O1), U29.6 (I/O1)
VBAT: C4.1, C23.1, C24.1, C25.1, C29.1, C30.1, C35.1, C36.1, C41.1, C42.1, C47.1, C48.1, C54.1, C63.1, C64.1, C74.1, C81.1, C82.1, C92.1, C99.1, C101.1, C108.1, C116.1, C193.1, C194.1, C197.1, C198.1, C219.1, C220.1, C221.1, C222.1, C223.1, D1.1 (K), D20.2 (A), D21.2 (A), Q10.5 (VBAT), Q11.5 (VBAT), Q15.5 (VBAT), Q17.5 (VBAT), Q21.5 (VBAT), Q28.5 (VBAT), Q32.5 (VBAT), R2.2, R17.1, R92.1, R96.1, R149.1, TP9.1, U1.1 (VBAT), U3.22 (VBAT), U4.2 (VBAT), U5.2 (VBAT), U5.3 (VBAT), U5.24 (VBAT), U6.2 (VBAT), U7.2 (VBAT), U7.3 (VBAT), U7.24 (VBAT), U12.3 (VBAT), U13.3 (VBAT), U15.3 (VBAT), U16.2 (VBAT), U16.3 (VBAT), U16.24 (VBAT), U19.2 (VBAT), U19.3 (VBAT), U19.24 (VBAT), U21.4 (VBAT), U22.4 (VBAT)
VBUS20: C20.1, C21.1, C22.1, C163.1, C178.1, C179.1, C180.1, C181.1, C182.1, C183.1, C184.1, C185.1, C186.1, C187.1, C188.1, C189.1, C192.1, C199.1, C200.1, C201.1, C202.1, C203.1, C204.1, C205.1, C206.1, R6.1, R11.2, R16.1, R147.1, R161.1, R197.1, R202.1, R203.1, R204.1, R205.1, TP12.1, U2.12 (VBUS20), U2.24 (VBUS20), U3.1 (VBUS20)
VBUS_WALL: C156.1, J_USBW.1, U29.5 (VBUS), U32.5 (VBUS_WALL)
VHEAT: C161.1, C162.1, J_HEAT.1, L12.2, R191.1
VHEAT_IN: C159.1, C160.1, R193.1, U22.5 (VHEAT_IN), U33.3 (VHEAT_IN)
VIN_RAW: C11.1, C12.1, D2.1 (K), D19.2 (A), J_DOCK.1, J_DOCK.2, J_DOCK.3, J_DOCK.4, Q2.5 (VIN_RAW), R14.1, R195.1, R196.1, R200.1, TP13.1
VMON: J_MON.1, U21.5 (VMON)
ZEROIZE_HW: J_AB1.20, J_MEZZ1.15, R117.1

Notes on the sheet:
PCB-A POWER + I/O A65
PACK NODE OVER THE DOCK BLOCK (32.56) | MAIN POWER CONTROL LTC2954 | FRONT END
PACK NODE OVER THE DOCK BLOCK (32.56): 9 A PINS, PRE-CHARGE, 25 A BLADE, DOCK SIGNAL PINS
MAIN POWER CONTROL LTC2954
FRONT END: LM5176 FROM THE 9 TO 36 V INPUT TO THE 20 V CHARGE BUS
page 1 of 14 MeshSat field kit V2, CERN-OHL-S-2.0 PROTOTYPE, nothing built 2026-09-26
spring pins to the dock block
25 A mini blade
SMCJ18A
9 A spring pin
pre-charge pin
LTC2954ITS8-1 push-button on/off c..
2N7002
JST-XH 1x2 socket
LM5176PWPR buck-boost controller
BAT46W-7-F Schottky 100V
1u 100V
100k
40.2k
10uH XAL1010-103ME
p13
p14
p7,14
p12
FRONT END
FRONT END: LM5176 FROM THE 9 TO 36 V INPUT TO THE 20 V CHARGE BUS (continued)
page 2 of 14 MeshSat field kit V2, CERN-OHL-S-2.0 PROTOTYPE, nothing built 2026-09-26
decoupling of U2
330u 35V
10u 50V
CSD19532Q5B 100 V N-FET
10u 100V
SMCJ40A
5mOhm 1%
10mOhm 1%
TPS37A010122DSKR 65 V OV/UV superv..
BZT52C12-7-F zener
FRONT END | CHARGER BQ25731
CHARGER BQ25731: 4S FROM THE 20 V BUS, SYSTEM ON VSYS (VBAT), PACK BEYOND RSR, I2C 0x6B
page 3 of 14 MeshSat field kit V2, CERN-OHL-S-2.0 PROTOTYPE, nothing built 2026-09-26
510R 1W
BQ25731RSNR 1 to 5 cell buck-boost..
13.3k 1%
10k
3.3uH XAL6030-332ME
22u 25V
SLOT RAIL S1 | SLOT RAIL S2
SLOT RAIL S1: AP64500 5.1 V + INA226 0x40
SLOT RAIL S2: LM5176 5.1 V (7.2 A MINIMUM LIMIT) + INA226 0x41
page 4 of 14 MeshSat field kit V2, CERN-OHL-S-2.0 PROTOTYPE, nothing built 2026-09-26
AP64500SP-13 5 A buck
68k
4.7uH XAL6060-472ME
10u 25V
22u 10V
slot 1 5.1 V rail to B16
100R 1%
6.8uH XAL1010-682ME
150u 25V
6mOhm 1%
p5,6,8,9,..
p3,5,6,8,..
SLOT RAIL S2 | SLOT RAIL S3
SLOT RAIL S2: LM5176 5.1 V (7.2 A MINIMUM LIMIT) + INA226 0x41 (continued)
SLOT RAIL S3: AP64500 5.1 V + INA226 0x44
page 5 of 14 MeshSat field kit V2, CERN-OHL-S-2.0 PROTOTYPE, nothing built 2026-09-26
slot 2 5.1 V rail to B16
slot 3 5.1 V rail to B16
p3,4,6,8,..
p4,6,8,9,..
DEVICE RAIL
DEVICE RAIL: LM5176 5.1 V (7.2 A MINIMUM LIMIT) + INA226 0x45
page 6 of 14 MeshSat field kit V2, CERN-OHL-S-2.0 PROTOTYPE, nothing built 2026-09-26
decoupling of U7
USB device rail to B16
p3,4,5,8,..
3.3 V LOGIC | PA RAIL
3.3 V LOGIC: TPS62933
PA RAIL: LM5176 13.8 V 6 A, EMCON GATED, INA226 0x46
page 7 of 14 MeshSat field kit V2, CERN-OHL-S-2.0 PROTOTYPE, nothing built 2026-09-26
TPS62933DRLR 3 A buck
4.7uH
470u 25V
p1,14
p12,13
p8,14
PA RAIL | HF RAIL
PA RAIL: LM5176 13.8 V 6 A, EMCON GATED, INA226 0x46 (continued)
HF RAIL: LM5176 12.0 V 2 A, EMCON GATED
page 8 of 14 MeshSat field kit V2, CERN-OHL-S-2.0 PROTOTYPE, nothing built 2026-09-26
INA226 PA rail monitor
13.8 V to the PA module on the fac..
12.0 V to the QMX HF unit in its l..
p3,4,5,6,..
POE RAIL
POE RAIL: LM5176 BOOST 54 V 0.6 A, INA226 0x47
page 9 of 14 MeshSat field kit V2, CERN-OHL-S-2.0 PROTOTYPE, nothing built 2026-09-26
15uH XAL1010-153ME
decoupling of U16
20mOhm 1%
INA226 PoE rail monitor
54 V to the PoE injector on B16
p4,5,6,8,..
USB-C PD OUTLET
USB-C PD OUTLET: TPS25740A + LM5176 5/9/15 V STAGE
page 10 of 14 MeshSat field kit V2, CERN-OHL-S-2.0 PROTOTYPE, nothing built 2026-09-26
20k 1%
21.0k 1%
14.0k 1%
470u 25V Panasonic EEHZK1E471P hyb..
decoupling of U19
10mOhm 1% 2512
p11
p11,14
USB-C PD OUTLET | EFUSES
USB-C PD OUTLET: TPS25740A + LM5176 5/9/15 V STAGE (continued)
EFUSES: MONITOR, HEATER (12.0 V BUCK), D8 5 V
page 11 of 14 MeshSat field kit V2, CERN-OHL-S-2.0 PROTOTYPE, nothing built 2026-09-26
TPS25740ARGER USB-C PD source cont..
SMBJ18A
43R 1W 2512
CSD18510Q5B 40 V N-FET
wall USB-C outlet
TPD2E2U06QDBZRQ1 low-capacitance E..
TPS259631DDAR eFuse VBAT -> VMON
750R 1%
10k 1%
monitor supply lead to the Xenarc
TPS259631DDAR eFuse VBAT -> VHEAT_IN
909R 1%
15uH XAL4040-153ME
p10
p10,14
EFUSES | EMCON GATES 74AUP1G08 (BOTH LINES), OUTLET INTERLOCK 74LVC08, EXPANDERS 0x21 0x24
EFUSES: MONITOR, HEATER (12.0 V BUCK), D8 5 V (continued)
EMCON GATES 74AUP1G08 (BOTH LINES), OUTLET INTERLOCK 74LVC08, EXPANDERS 0x21 0x24
page 12 of 14 MeshSat field kit V2, CERN-OHL-S-2.0 PROTOTYPE, nothing built 2026-09-26
TPS259631DDAR eFuse +5V_DEV -> +5V..
453R 1%
D8 mezzanine 5 V
SN74AUP1G08DBVR AND
SN74LVC08APWR quad AND
SN74LVC1G00DBVR NAND
PCA9555PW
p13,14
p7,13
EMCON GATES 74AUP1G08 (BOTH LINES), OUTLET INTERLOCK 74LVC08, EXPANDERS 0x21 0x24 | RIBBON J_AB1 2x13, WALL-PORT RIBBON J_AB2 2x5, MEZZANINE HARNESS J_MEZZ1 2x8, GLENAI
EMCON GATES 74AUP1G08 (BOTH LINES), OUTLET INTERLOCK 74LVC08, EXPANDERS 0x21 0x24 (continued)
RIBBON J_AB1 2x13, WALL-PORT RIBBON J_AB2 2x5, MEZZANINE HARNESS J_MEZZ1 2x8, GLENAIR WALL USB HOST PORT
ELEVEN BLIND-MATE RF SITES: SMA JACK (TOP) + SMP-MAX RECEPTACLE (UNDERSIDE)
page 13 of 14 MeshSat field kit V2, CERN-OHL-S-2.0 PROTOTYPE, nothing built 2026-09-26
A-B interconnect
A-B wall-port ribbon
D8 mezzanine harness
JST-PH 1x4 socket
TPS259631DDAR eFuse +5V_DEV -> VBU..
1k 1%
SMA jack
SMP-MAX slide-on receptacle R222M0..
p12,14
p7,12
ELEVEN BLIND-MATE RF SITES | TEST POINTS, FLAGS | OTHER PARTS (not in a section list)
ELEVEN BLIND-MATE RF SITES: SMA JACK (TOP) + SMP-MAX RECEPTACLE (UNDERSIDE) (continued)
TEST POINTS, FLAGS
OTHER PARTS (not in a section list)
page 14 of 14 MeshSat field kit V2, CERN-OHL-S-2.0 PROTOTYPE, nothing built 2026-09-26
p1,7
p1,12
p10,11
p7,8
