meshsat/meshsat-fieldkit/v2/release/handover/H1/v2/ecad/pcb-b-compute-b19/pcb-b-compute.kicad_sch

## KiCad design v2/release/handover/H1/v2/ecad/pcb-b-compute-b19/pcb-b-compute.kicad_sch (2026-09-26)

Schematic: pcb-b-compute.kicad_sch

Parts:
BT1: CR2032 holder Keystone 3034: VBAT for the three m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; BatteryHolder_Keystone_3034_1x20mm
C1, C2, C101, C102, C103, C104, C201, C202, C203, C204, C301, C302, C303, C304: 100u 10V; C_1206_3216Metric
C3, C10, C17, C18, C19, C20, C21, C22, C23, C24, C25, C26, C29, C30, C31, C32, C36, C37, C38, C40, C44, C47, C49, C51, C54, C55, C57, C60, C62, C65, C66, C67, C68, C69, C70, C71, C110, C111, C118, C128, C133, C135, C136, C137, C138, C139, C140, C141, C142, C143, C144, C145, C146, C150, C158, C166, C167, C168, C169, C170, C171, C172, C173, C192, C194, C197, C210, C211, C218, C228, C233, C235, C236, C237, C238, C239, C240, C241, C242, C243, C244, C245, C246, C250, C258, C266, C267, C268, C269, C270, C271, C272, C273, C286, C289, C292, C294, C297, C310, C311, C318, C328, C333, C335, C336, C337, C338, C339, C340, C341, C342, C343, C344, C345, C346, C350, C358, C366, C367, C368, C369, C370, C371, C372, C373, C392, C394, C397, C402, C403, C404, C405, C406, C409, C422, C423, C424, C425, C426, C429, C442, C443, C444, C445, C446, C449, C470, C471, C472, C473, C474, C475, C476, C477, C478, C479, C480: 100n; C_0603_1608Metric
C4, C7, C16, C27, C28, C39, C41, C46, C53, C64, C105, C106, C107, C108, C109, C125, C130, C147, C148, C174, C205, C206, C207, C208, C209, C225, C230, C247, C248, C274, C305, C306, C307, C308, C309, C325, C330, C347, C348, C374, C401, C421, C441: 10u; C_0805_2012Metric
C5, C6, C8, C9, C58, C63, C126, C127, C131, C132, C149, C157, C226, C227, C231, C232, C249, C257, C326, C327, C331, C332, C349, C357: 22u 6.3V; C_0805_2012Metric
C11, C56, C61, C129, C134, C229, C234, C329, C334, C481, C482, C483: 10n; C_0603_1608Metric
C12, C13, C163, C193, C263, C293, C363, C393, C400, C420, C440: 1u; C_0603_1608Metric
C14, C15, C164, C165, C264, C265, C364, C365, C410, C411, C430, C431, C450, C451: 18p; C_0402_1005Metric
C33: 1n 2kV; C_1812_4532Metric
C34: 100n 100V; C_0805_2012Metric; LCSC C106243
C35: 10u 100V; C_1210_3225Metric; LCSC C576517
C42: 47p; C_0402_1005Metric
C43, C48, C50, C59: 4.7u; C_0805_2012Metric
C45, C52: 1n; C_0603_1608Metric
C112, C113, C114, C115, C116, C119, C120, C121, C122, C123, C212, C213, C214, C215, C216, C219, C220, C221, C222, C223, C312, C313, C314, C315, C316, C319, C320, C321, C322, C323: 22u 10V X7R 1210; C_1210_3225Metric
C117, C124, C217, C224, C317, C324: 3.3n; C_0603_1608Metric
C151, C152, C251, C252, C351, C352: 220n 16V (PCIe AC coupling, CM5 datasheet 2.3.1); C_0402_1005Metric
C153, C154, C155, C156, C253, C254, C255, C256, C353, C354, C355, C356: 220n 16V (PCIe AC coupling at the switch transmit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; C_0402_1005Metric
C159, C160, C161, C162, C175, C176, C177, C178, C179, C180, C181, C182, C259, C260, C275, C276, C277, C278, C279, C280, C281, C282, C359, C360, C375, C376, C377, C378, C379, C380, C381, C382, C525: 100n; C_0402_1005Metric
C195, C196, C295, C296, C395, C396: 100n 16V (REFCLK AC coupling, DS40068 3.1, W3-F03); C_0402_1005Metric
C283, C284, C287, C288, C290, C291: 10p 50V C0G; C_0402_1005Metric; LCSC C106199
C298, C524, C527: 68p 50V C0G; C_0402_1005Metric; LCSC C107009
C407, C408, C427, C428, C447, C448: 2.2u; C_0603_1608Metric
C460, C461, C506, C507: 4.7n; C_0603_1608Metric
C500, C501, C502, C503, C504, C505: 22p; C_0402_1005Metric
C520, C521: 220u 6.3V KEMET T520B227M006ATE025 polymer tantal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; CP_EIA-3528-21_Kemet-B; LCSC C212684
C522: 6.8n 50V X7R; C_0402_1005Metric; LCSC C93654
C523, C526: 220p 50V C0G; C_0402_1005Metric; LCSC C107001
C528: 15p 50V C0G; C_0402_1005Metric; LCSC C106997
C529: 9.1p 50V C0G; C_0402_1005Metric; LCSC C526972
C530: 4.7p 50V C0G; C_0402_1005Metric; LCSC C325453
D1: SMBJ5.0A; D_SMB
D2: SMBJ58A; D_SMB; LCSC C135085
D101, D201, D301: SMBJ6.0A (6.0 V standoff on the 5.1 V slot rail); D_SMB; LCSC C83270
D520: SMBJ5.0A; D_SMB; LCSC C113974
F1: 2A hold 1812; Fuse_1812_4532Metric
F2, F3: 0.5A hold 1812; Fuse_1812_4532Metric
J_5V_DEV: JST-VH socket, 10 A: USB device rail from A22 J_5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; JST_VH_B2P-VH_1x02_P3.96mm_Vertical; LCSC C274411
J_5V_S1: JST-VH socket, 10 A: 5 V slot rail S1 from A22 J_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; JST_VH_B2P-VH_1x02_P3.96mm_Vertical; LCSC C274411
J_5V_S2: JST-VH socket, 10 A: 5 V slot rail S2 from A22 J_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; JST_VH_B2P-VH_1x02_P3.96mm_Vertical; LCSC C274411
J_5V_S3: JST-VH socket, 10 A: 5 V slot rail S3 from A22 J_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; JST_VH_B2P-VH_1x02_P3.96mm_Vertical; LCSC C274411
J_54V: JST-VH socket, 10 A: 54 V PoE feed from A22 J_54V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; JST_VH_B2P-VH_1x02_P3.96mm_Vertical; LCSC C274411
J_AB1: A-B interconnect (IDC 2x13, underside, mates A22'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; IDC-Header_2x13_P2.54mm_Vertical_NarrowPad
J_AB2: A-B wall-port ribbon (IDC 2x5): the wall USB pair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; IDC-Header_2x05_P2.54mm_Vertical_NarrowPad
J_CAM: camera lead (USB 2.0, bank 1 hub, port 3): 5V D- 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; PinHeader_1x04_P2.54mm_Vertical
J_DBG1: console UART0 and the module I2C of S1 (3.3 V, be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; PinHeader_1x05_P2.54mm_Vertical
J_DBG2: console UART0 and the module I2C of S2 (3.3 V, be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; PinHeader_1x05_P2.54mm_Vertical
J_DBG3: console UART0 and the module I2C of S3 (3.3 V, be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; PinHeader_1x05_P2.54mm_Vertical
J_ETH: RJ45 jack (Amphenol RJHSE5380): patch lead to the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; RJ45_Amphenol_RJHSE5380
J_FAN1: IP68 cooler fan of S1 (JST-SH 1.0): 5V GND TACHO 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; JST_SH_BM04B-SRSS-TB_1x04-1MP_P1.00mm_Vertical; LCSC C160390
J_FAN2: IP68 cooler fan of S2 (JST-SH 1.0): 5V GND TACHO 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; JST_SH_BM04B-SRSS-TB_1x04-1MP_P1.00mm_Vertical; LCSC C160390
J_FAN3: IP68 cooler fan of S3 (JST-SH 1.0): 5V GND TACHO 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; JST_SH_BM04B-SRSS-TB_1x04-1MP_P1.00mm_Vertical; LCSC C160390
J_FLASH1, J_FLASH2, J_FLASH3: USB-C 2.0 receptacle; USB_C_Receptacle_HRO_TYPE-C-31-M-12; LCSC C165948
J_GNSS1: U.FL socket: pigtail to A22's GNSS jack J_RF4; U.FL_Hirose_U.FL-R-SMT-1_Vertical; LCSC C88373
J_GNSS2: LG290P UART2 (bench): GND TX RX; PinHeader_1x03_P2.54mm_Vertical
J_HDMI: HDMI type A receptacle (Molex 208658-1001): cable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; HDMI_A_Molex_208658-1001_Horizontal; LCSC C916313
J_IOCOFF_A: bench jumper, controller A: fit to hold its LDO o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; PinHeader_1x02_P2.54mm_Vertical_SMD_Pin1Left
J_IOCOFF_B: bench jumper, controller B: fit to hold its LDO o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; PinHeader_1x02_P2.54mm_Vertical_SMD_Pin1Left
J_IOCOFF_C: bench jumper, controller C: fit to hold its LDO o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; PinHeader_1x02_P2.54mm_Vertical_SMD_Pin1Left
J_LIME: USB 3.0 type A receptacle (Wuerth 692122030100 la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; USB3_A_Receptacle_Wuerth_692122030100; LCSC C5355286
J_LORA1: U.FL socket: pigtail to A22's LoRa jack J_RF11; U.FL_Hirose_U.FL-R-SMT-1_Vertical; LCSC C88373
J_M2C1, J_M2C3: M.2 E-key 2230 socket, TE 2199230-4, M2.5 standof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; M2_E-Key_Socket_2230; LCSC C2977809
J_M2C2: M.2 B-key 3052 socket, TE 2199119-3, M2.5 standof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; M2_B-Key_Socket_3052; LCSC C590866
J_M2N1, J_M2N2, J_M2N3: M.2 M-key 2242 socket, Amphenol MDT420M02001, M2.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; M2_M-Key_Socket_2242; LCSC C2927698
J_PANEL: panel ribbon to PCB-C C7 (IDC 2x13): the RP2040 p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; IDC-Header_2x13_P2.54mm_Vertical_NarrowPad
J_QMX: QMX USB lead (bank 2 hub, port 4): VBUS D- D+ GND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; PinHeader_1x04_P2.54mm_Vertical
J_RB9704: RockBLOCK 9704 16-pin (IDC 2x8) on the Ground Con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; IDC-Header_2x08_P2.54mm_Vertical_NarrowPad
J_RPIBOOT1: nRPIBOOT jumper S1: fit to flash the eMMC over J_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; PinHeader_1x02_P2.54mm_Vertical
J_RPIBOOT2: nRPIBOOT jumper S2: fit to flash the eMMC over J_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; PinHeader_1x02_P2.54mm_Vertical
J_RPIBOOT3: nRPIBOOT jumper S3: fit to flash the eMMC over J_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; PinHeader_1x02_P2.54mm_Vertical
J_SIM1: nano-SIM push-push GCT SIM8060 (SIM 1); nanoSIM_GCT_SIM8060-6-0-14-00; LCSC C6296715
J_SIM2: nano-SIM push-push GCT SIM8060 (SIM 2); nanoSIM_GCT_SIM8060-6-0-14-00; LCSC C6296715
J_SPI3: SPI0 breakout of S3 (2x5): 3V3 GND MISO MOSI SCLK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; PinHeader_2x05_P2.54mm_Vertical
J_W1A, J_W1B: U.FL: MHF4 pigtail from the slot 1 WiFi card, cha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; U.FL_Hirose_U.FL-R-SMT-1_Vertical; LCSC C434808
J_W3A, J_W3B: U.FL: MHF4 pigtail from the slot 3 WiFi card, cha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; U.FL_Hirose_U.FL-R-SMT-1_Vertical; LCSC C434808
J_WOA: U.FL: pigtail to A22's P2P jack, chain A; U.FL_Hirose_U.FL-R-SMT-1_Vertical; LCSC C434808
J_WOB: U.FL: pigtail to A22's P2P jack, chain B; U.FL_Hirose_U.FL-R-SMT-1_Vertical; LCSC C434808
J_ZBDBG1: CC2652P cJTAG ZBA (bench): 3V3 GND TMSC TCKC RESET; PinHeader_1x05_P2.54mm_Vertical
J_ZBDBG2: CC2652P cJTAG ZBB (bench): 3V3 GND TMSC TCKC RESET; PinHeader_1x05_P2.54mm_Vertical
L1: 4.7uH XAL4030-472ME; L_Coilcraft_XAL4020-XXX
L2, L103, L104, L203, L204, L303, L304: 2.2uH XAL4020-222ME; L_Coilcraft_XAL4020-XXX
L3: 27nH 0402 (antenna bias tee); L_0402_1005Metric; LCSC C12669
L101, L102, L201, L202, L301, L302: 3.3uH XAL6030-332ME; L_Coilcraft_XAL6060-XXX
LED1: green Ethernet port 1 link; LED_0603_1608Metric; LCSC C12624
LED2: green Ethernet port 2 link; LED_0603_1608Metric; LCSC C12624
LED3: green Ethernet port 3 link; LED_0603_1608Metric; LCSC C12624
LED4: green Ethernet port 4 link; LED_0603_1608Metric; LCSC C12624
LED6: red ZBA (DIO_7); LED_0603_1608Metric; LCSC C2286
LED7: green ZBA (DIO_8); LED_0603_1608Metric; LCSC C12624
LED8: red ZBB (DIO_7); LED_0603_1608Metric; LCSC C2286
LED9: green ZBB (DIO_8); LED_0603_1608Metric; LCSC C12624
LED11: green 5 V S1; LED_0603_1608Metric; LCSC C12624
LED12, LED22, LED32: green NVMe link (PORTSTATUS0); LED_0603_1608Metric; LCSC C12624
LED13, LED23, LED33: green card link (PORTSTATUS1); LED_0603_1608Metric; LCSC C12624
LED14, LED24, LED34: amber NVMe activity; LED_0603_1608Metric; LCSC C2287
LED15: blue WiFi link; LED_0603_1608Metric; LCSC C2288
LED16, LED26, LED36: green ACT (LED_nACT sinks); LED_0603_1608Metric; LCSC C12624
LED17, LED27, LED37: red PWR; LED_0603_1608Metric; LCSC C2286
LED21: green 5 V S2; LED_0603_1608Metric; LCSC C12624
LED25: amber 5G network; LED_0603_1608Metric; LCSC C2287
LED31: green 5 V S3; LED_0603_1608Metric; LCSC C12624
LED35: blue WiFi link, card 2; LED_0603_1608Metric; LCSC C2288
LED40: green IOCTRL A alive; LED_0603_1608Metric; LCSC C12624
LED41: green IOCTRL B alive; LED_0603_1608Metric; LCSC C12624
LED42: green IOCTRL C alive; LED_0603_1608Metric; LCSC C12624
Q1: CSD19532Q5B 100 V N-FET (4.6 mOhm at VGS 6 V, Pow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; PowerPAK_SO-8_Single; LCSC C473333
Q2: 2N7002 expander -> switch reset; SOT-23; LCSC C8545
Q3, Q4, Q5: 2N7002: a voted majority pulls the bank's hub int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; SOT-23; LCSC C8545
Q10: 2N7002: the changeover's complement, so a voted W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; SOT-23; LCSC C8545
Q11: 2N7002: EMCON_ON = NOT EMCON_HW (S-01); SOT-23; LCSC C8545
Q101, Q201, Q301: BC857: LED_nPWR must be buffered (datasheet Table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; SOT-23
Q102, Q103, Q104, Q105, Q202, Q203, Q204, Q205, Q302, Q303, Q304, Q305: 2N7002; SOT-23; LCSC C8545
Q106, Q206, Q306: 2N7002: EMCON_ON pulls W_DISABLE1# low (open drai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; SOT-23; LCSC C8545
Q109, Q209, Q309: 2N7002: pulls WL_nDisable low only (S-01); SOT-23; LCSC C8545
Q110, Q210, Q310: 2N7002: pulls BT_nDisable low only (S-01); SOT-23; LCSC C8545
Q111, Q311: 2N7002: EMCON removes the WiFi card's supply (S-0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; SOT-23; LCSC C8545
Q207: 2N7002 expander -> FULL_CARD_POWER_OFF#; SOT-23; LCSC C8545
Q208: 2N7002 expander -> RESET# (open drain, no pull-up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; SOT-23; LCSC C8545
R1, R103, R108, R113, R115, R144, R203, R208, R213, R215, R244, R303, R308, R313, R315, R344: 10k 1%; R_0603_1608Metric
R2: 20.0k 1%; R_0603_1608Metric
R3: 6.04k 1% (ISET); R_0603_1608Metric
R4, R11, R14, R21, R22, R25, R28, R29, R30, R31, R37, R41, R42, R44, R47, R56, R58, R63, R64, R75, R76, R87, R88, R132, R133, R134, R135, R137, R138, R141, R145, R146, R149, R151, R154, R155, R156, R157, R158, R162, R163, R164, R232, R233, R234, R235, R237, R238, R241, R245, R246, R249, R251, R254, R255, R256, R257, R258, R262, R263, R332, R333, R334, R335, R337, R338, R341, R345, R346, R349, R351, R354, R355, R356, R357, R358, R362, R363, R364, R474, R475, R476, R510, R513, R514, R515, R516, R517: 10k; R_0603_1608Metric
R5, R6, R7, R8, R24, R26, R27, R32, R33, R34, R35, R40, R65, R77, R89, R101, R129, R130, R131, R136, R139, R148, R150, R201, R229, R230, R231, R236, R239, R248, R250, R301, R329, R330, R331, R336, R339, R348, R350: 1k; R_0603_1608Metric
R9, R10: 75; R_0603_1608Metric
R12: 0.25R 1% 2512; R_2512_6332Metric
R13: 0R 2512 (POE_P link); R_2512_6332Metric
R15, R16, R49, R59, R66, R78, R90, R106, R111, R112, R160, R161, R173, R174, R206, R211, R212, R260, R261, R273, R274, R306, R311, R312, R360, R361, R373, R374, R477, R478, R479, R480, R481, R482, R483, R484, R485, R486, R487, R488, R489, R490, R491, R492, R493, R494, R495, R496, R497, R498, R499, R500: 100k; R_0603_1608Metric
R17, R18, R54, R55: 2.2k; R_0603_1608Metric
R19: 15k; R_0603_1608Metric
R20, R105, R110, R210, R305, R310: 22k; R_0603_1608Metric
R23: 10R; R_0603_1608Metric
R36, R43: 301R 1% (ILM: 3.0 A); R_0603_1608Metric
R38, R45: 100k 1%; R_0603_1608Metric
R39, R46: 10k 1% (OVLO); R_0603_1608Metric
R48, R50, R51, R52, R53, R60, R61, R62, R127, R227, R327: 4.7k; R_0603_1608Metric
R57: 1k (strap [LED4_1, LED3_1] = 01: I2C management, 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; R_0603_1608Metric
R102, R107, R207, R302, R307: 31.6k 1%; R_0603_1608Metric
R104, R109, R204, R209, R304, R309: 68k (RT: 500 kHz); R_0603_1608Metric
R114, R214, R314: 40.2k 1%; R_0603_1608Metric
R116, R216, R316: 26.7k 1%; R_0603_1608Metric
R117, R217, R317: 475 1% (IREF); R_0603_1608Metric
R118, R218, R318: 1.43k 1% (REXT); R_0603_1608Metric
R119, R120, R121, R123, R125, R126, R152, R153, R219, R220, R221, R223, R225, R226, R252, R253, R319, R320, R321, R323, R325, R326, R352, R353: 5.1k; R_0603_1608Metric
R122, R124, R128, R222, R224, R228, R322, R324, R328: 330; R_0603_1608Metric
R142, R242, R342: 9.53k 1%; R_0603_1608Metric
R143, R243, R343: 90.9k 1%; R_0603_1608Metric
R147, R247, R347: 1M; R_0603_1608Metric
R165, R265, R365: 5mOhm 1% 2512 (Kelvin shunt: card socket current,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; R_2512_6332Metric; LCSC C500739
R175, R176, R179, R180, R183, R184, R275, R276, R279, R280, R283, R284, R375, R376, R379, R380, R383, R384: 33.2R 1% (HCSL series Rs, DS40068 Table 8-1, W3-F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; R_0603_1608Metric; LCSC C23004
R177, R178, R181, R182, R185, R186, R277, R278, R281, R282, R285, R286, R377, R378, R381, R382, R385, R386: 49.9R 1% (HCSL shunt Rp, DS40068 Table 8-1, W3-F0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; R_0603_1608Metric; LCSC C23185
R202: 33.2k 1%; R_0603_1608Metric; LCSC C23003
R205: 120k 1%; R_0603_1608Metric; LCSC C25808
R266, R267, R268, R269, R270, R271: 22R; R_0603_1608Metric
R272, R287, R288, R289: 0R (eSIM option link at the module, HD 4.1.6 Figu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; R_0603_1608Metric; LCSC C21189
R470, R471, R472, R473, R504, R505, R506, R507: 60R4 1%; R_0603_1608Metric
R508, R509: 0R (break link: remove to cut fabric A between co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; R_0603_1608Metric; LCSC C21189
R511, R512: 0R (break link: remove to cut fabric B between co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; R_0603_1608Metric; LCSC C21189
T1: Pulse H5007NL 1000BASE-T magnetics (switch port 4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; Pulse_H5007NL; LCSC C6384935
TP2: +5V_DEV; TestPoint_Pad_D1.5mm
TP3: +3V3_DEV; TestPoint_Pad_D1.5mm
TP4: +1V2_KSZ; TestPoint_Pad_D1.5mm
TP5: +2V5_KSZ; TestPoint_Pad_D1.5mm
TP6: VBAT; TestPoint_Pad_D1.5mm
TP7: EMCON_HW; TestPoint_Pad_D1.5mm
TP8: ZEROIZE_HW; TestPoint_Pad_D1.5mm
TP9: GNSS_PPS; TestPoint_Pad_D1.5mm
TP10: SDA; TestPoint_Pad_D1.5mm
TP11: SCL; TestPoint_Pad_D1.5mm
TP12: +54V_POE; TestPoint_Pad_D1.5mm
TP13: POE_DRAIN; TestPoint_Pad_D1.5mm
TP14: +5V_LIME; TestPoint_Pad_D1.5mm
TP15: +5V_RB; TestPoint_Pad_D1.5mm
TP16: +5V_LORA; TestPoint_Pad_D1.5mm
TP17: +3V3_ZB; TestPoint_Pad_D1.5mm
TP18: HDMI_SEL1; TestPoint_Pad_D1.5mm
TP19: HDMI_SEL2; TestPoint_Pad_D1.5mm
TP20, TP102: +3V3_S1A; TestPoint_Pad_D1.5mm
TP21: +3V3_S1B; TestPoint_Pad_D1.5mm
TP22: +1V0_S1; TestPoint_Pad_D1.5mm
TP23: +1V1_S1; TestPoint_Pad_D1.5mm
TP24, TP202: +3V3_S2A; TestPoint_Pad_D1.5mm
TP25: +3V3_S2B; TestPoint_Pad_D1.5mm
TP26: +1V0_S2; TestPoint_Pad_D1.5mm
TP27: +1V1_S2; TestPoint_Pad_D1.5mm
TP28, TP302: +3V3_S3A; TestPoint_Pad_D1.5mm
TP29: +3V3_S3B; TestPoint_Pad_D1.5mm
TP30: +1V0_S3; TestPoint_Pad_D1.5mm
TP31: +1V1_S3; TestPoint_Pad_D1.5mm
TP41: EXP_SPARE1; TestPoint_Pad_D1.5mm
TP42: EXP_SPARE2; TestPoint_Pad_D1.5mm
TP43: EXP_SPARE3; TestPoint_Pad_D1.5mm
TP44: EXP_SPARE4; TestPoint_Pad_D1.5mm
TP45: EXP_SPARE5; TestPoint_Pad_D1.5mm
TP46: EXP_SPARE6; TestPoint_Pad_D1.5mm
TP47: EXP_SPARE7; TestPoint_Pad_D1.5mm
TP48: EXP_SPARE8; TestPoint_Pad_D1.5mm
TP49: EXP_SPARE9; TestPoint_Pad_D1.5mm
TP50: EXP_SPARE10; TestPoint_Pad_D1.5mm
TP51: EXP_SPARE11; TestPoint_Pad_D1.5mm
TP101, TP201, TP301, TP501, TP502, TP503: GND; TestPoint_Pad_D1.5mm
TP103: +3V3_M2C1; TestPoint_Pad_D1.5mm
TP203: +3V3_M2C2; TestPoint_Pad_D1.5mm
TP303: +3V3_M2C3; TestPoint_Pad_D1.5mm
TP504: BSEL1; TestPoint_Pad_D1.5mm
TP505: BSEL2; TestPoint_Pad_D1.5mm
TP506: BSEL3; TestPoint_Pad_D1.5mm
TP507: BOE1_n; TestPoint_Pad_D1.5mm
TP508: BOE2_n; TestPoint_Pad_D1.5mm
TP509: BOE3_n; TestPoint_Pad_D1.5mm
TP510: WIFI_SEC; TestPoint_Pad_D1.5mm
TP511: HUBRST1_VOTE; TestPoint_Pad_D1.5mm
TP512: HUBRST2_VOTE; TestPoint_Pad_D1.5mm
TP513: HUBRST3_VOTE; TestPoint_Pad_D1.5mm
TP514: SEL1_A; TestPoint_Pad_D1.5mm
TP515: SEL1_B; TestPoint_Pad_D1.5mm
TP516: SEL1_C; TestPoint_Pad_D1.5mm
TP517: SEL2_A; TestPoint_Pad_D1.5mm
TP518: SEL2_B; TestPoint_Pad_D1.5mm
TP519: SEL2_C; TestPoint_Pad_D1.5mm
TP520: SEL3_A; TestPoint_Pad_D1.5mm
TP521: SEL3_B; TestPoint_Pad_D1.5mm
TP522: SEL3_C; TestPoint_Pad_D1.5mm
TP523: HUBRST1_A; TestPoint_Pad_D1.5mm
TP524: HUBRST1_B; TestPoint_Pad_D1.5mm
TP525: HUBRST1_C; TestPoint_Pad_D1.5mm
TP526: HUBRST2_A; TestPoint_Pad_D1.5mm
TP527: HUBRST2_B; TestPoint_Pad_D1.5mm
TP528: HUBRST2_C; TestPoint_Pad_D1.5mm
TP529: HUBRST3_A; TestPoint_Pad_D1.5mm
TP530: HUBRST3_B; TestPoint_Pad_D1.5mm
TP531: HUBRST3_C; TestPoint_Pad_D1.5mm
TP532: WSEC_A; TestPoint_Pad_D1.5mm
TP533: WSEC_B; TestPoint_Pad_D1.5mm
TP534: WSEC_C; TestPoint_Pad_D1.5mm
TP535: CANH_A; TestPoint_Pad_D1.5mm
TP536: CANL_A; TestPoint_Pad_D1.5mm
TP537: CANH_B; TestPoint_Pad_D1.5mm
TP538: CANL_B; TestPoint_Pad_D1.5mm
U1: Microchip KSZ9897RTXI seven-port Gigabit switch: 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; TQFP-128_14x14mm_P0.4mm_EP10.0; LCSC C638299
U3: TI TS3DV642A0RUAR HDMI 2:1 switch (HDMI1 / HDMI2 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; WQFN-42-1EP_3.5x9mm_P0.5mm_EP2.05x7.55mm; LCSC C157482
U4: TI TS3DV642A0RUAR HDMI 2:1 switch (HDMIM / HDMI3 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; WQFN-42-1EP_3.5x9mm_P0.5mm_EP2.05x7.55mm; LCSC C157482
U5: TI TPS23861PWR PoE PSE controller, port 1 to the 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; TSSOP-28_4.4x9.7mm_P0.65mm; LCSC C93245
U6: PCA9555PW 0x20: outputs (switch reset, rail enabl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; TSSOP-24_4.4x7.8mm_P0.65mm; LCSC C2864778
U7: PCA9555PW 0x25: inputs (faults, RockBLOCK status)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; TSSOP-24_4.4x7.8mm_P0.65mm; LCSC C2864778
U8: ATECC608B-SSHDA-T secure element (I2C 0x60): keys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; SOIC-8_3.9x4.9mm_P1.27mm; LCSC C1518769
U9: DS3231MZ+ holdover clock (I2C 0x68), CR2032 backed; SOIC-8_3.9x4.9mm_P1.27mm; LCSC C9866
U10: TMP117AIDRVR board temperature under the coolers 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; WSON-6-1EP_2x2mm_P0.65mm_EP1x1.6mm; LCSC C699536
U11: Quectel LG290P03AAMD GNSS RTK module: UART1 to th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; Quectel_LG290P; LCSC C29781241
U12: Ebyte E22-900M30S 1 W LoRa (SX1262) on S3 SPI0 CE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; Ebyte_E22-900M30S; LCSC C411294
U13: Ebyte E72-2G4M20S1E CC2652P (Zigbee coordinator):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; Ebyte_E72-2G4M20S1E
U14: Ebyte E72-2G4M20S1E CC2652P (OpenThread RCP for M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; Ebyte_E72-2G4M20S1E
U15: CP2102N-A02-GQFN28 USB-UART bridge (GNSS); QFN-28-1EP_5x5mm_P0.5mm_EP3.35x3.35mm; LCSC C964632
U16: CP2102N-A02-GQFN28 USB-UART bridge (ZBA); QFN-28-1EP_5x5mm_P0.5mm_EP3.35x3.35mm; LCSC C964632
U17: CP2102N-A02-GQFN28 USB-UART bridge (ZBB); QFN-28-1EP_5x5mm_P0.5mm_EP3.35x3.35mm; LCSC C964632
U18: CP2102N-A02-GQFN28 USB-UART bridge (RB); QFN-28-1EP_5x5mm_P0.5mm_EP3.35x3.35mm; LCSC C964632
U19: SN74LVC08APWR quad AND: LimeSDR (hub port power A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; TSSOP-14_4.4x5mm_P0.65mm; LCSC C465737
U20: SN74LVC08APWR quad AND: E72 radios (EMCON AND sof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; TSSOP-14_4.4x5mm_P0.65mm; LCSC C465737
U21, U22: TPS22810DRV; WSON-6-1EP_2x2mm_P0.65mm_EP1x1.6mm
U23: TPS259631DDAR eFuse +5V_DEV -> +5V_LIME (301R 1% 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; SOIC-8-1EP_3.9x4.9mm_P1.27mm_EP2.29x3mm; LCSC C2155778
U24: TPS259631DDAR eFuse +5V_DEV -> +5V_RB (301R 1% (I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; SOIC-8-1EP_3.9x4.9mm_P1.27mm_EP2.29x3mm; LCSC C2155778
U25: AP63203WU-7 3.3 V 2 A buck: the shared logic (+3V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; TSOT-23-6; LCSC C780769
U26: TPS62933DRLR buck 1.2 V Ethernet switch core; SOT-583-8; LCSC C3200405
U27: AP2112K-2.5 LDO: the switch's 2.5 V analog rail; SOT-23-5; LCSC C176945
U28: TPS2065CDBV; SOT-23-5
U29, U33, U34, U35, U37, U107, U207, U307: USBLC6-2SC6; SOT-23-6; LCSC C7519
U30A: Amphenol 10164227-1004A1RLF receptacle A, slot S1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; CM5_Conn_A_10164227; LCSC C7435219
U30B: Amphenol 10164227-1004A1RLF receptacle B, slot S1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; CM5_Conn_B_10164227; LCSC C7435219
U31A: Amphenol 10164227-1004A1RLF receptacle A, slot S2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; CM5_Conn_A_10164227; LCSC C7435219
U31B: Amphenol 10164227-1004A1RLF receptacle B, slot S2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; CM5_Conn_B_10164227; LCSC C7435219
U32A: Amphenol 10164227-1004A1RLF receptacle A, slot S3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; CM5_Conn_A_10164227; LCSC C7435219
U32B: Amphenol 10164227-1004A1RLF receptacle B, slot S3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; CM5_Conn_B_10164227; LCSC C7435219
U40, U50, U60: AP2112K-3.3 LDO: the private 3.3 V of controller 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; SOT-23-5
U41: STM32H743VIT6 I/O supervisor A: 2-of-3 quorum on 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; LQFP-100_14x14mm_P0.5mm; LCSC C114409
U42: SWD pads, controller A: 3V3 SWDIO SWCLK NRST GND; PinHeader_1x05_P2.54mm_Vertical_SMD_Pin1Left
U43, U44: TCAN334D CAN-FD transceiver, controller A on hear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; SOIC-8_3.9x4.9mm_P1.27mm; LCSC C2871143
U51: STM32H743VIT6 I/O supervisor B: 2-of-3 quorum on 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; LQFP-100_14x14mm_P0.5mm; LCSC C114409
U52: SWD pads, controller B: 3V3 SWDIO SWCLK NRST GND; PinHeader_1x05_P2.54mm_Vertical_SMD_Pin1Left
U53, U54: TCAN334D CAN-FD transceiver, controller B on hear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; SOIC-8_3.9x4.9mm_P1.27mm; LCSC C2871143
U61: STM32H743VIT6 I/O supervisor C: 2-of-3 quorum on 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; LQFP-100_14x14mm_P0.5mm; LCSC C114409
U62: SWD pads, controller C: 3V3 SWDIO SWCLK NRST GND; PinHeader_1x05_P2.54mm_Vertical_SMD_Pin1Left
U63, U64: TCAN334D CAN-FD transceiver, controller C on hear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; SOIC-8_3.9x4.9mm_P1.27mm; LCSC C2871143
U70, U71, U72, U73, U74, U75: SN74LVC08APWR quad 2-input AND: the 2-of-3 majori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; TSSOP-14_4.4x5mm_P0.65mm; LCSC C465737
U76, U77, U78, U79: SN74LVC32APWR quad 2-input OR: the 2-of-3 majorit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; TSSOP-14_4.4x5mm_P0.65mm; LCSC C352974
U80: 74LVC86APW quad exclusive-or: break-before-make o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; TSSOP-14_4.4x5mm_P0.65mm; LCSC C350562
U82: SKY13351-378LF SPDT antenna changeover, chain A: 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; Skyworks_SKY13351_MLPD-6_1x1mm; LCSC C129189
U83: SKY13351-378LF SPDT antenna changeover, chain B: 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; Skyworks_SKY13351_MLPD-6_1x1mm; LCSC C129189
U101: Diodes PI7C9X2G404SL PCIe 2.0 switch, slot S1: up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; LQFP-128_14x14mm_P0.4mm_EP6.0; LCSC C500767
U102: TI TUSB8041IRGCR four-port USB 3.0 hub, slot S1 (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; QFN-64-1EP_9x9mm_P0.5mm_EP4.7x4.7mm; LCSC C544686
U103: AP64500SP-13 5 A buck, 3.3 V rail +3V3_S1A; SOIC-8-1EP_3.9x4.9mm_P1.27mm_EP2.29x3mm; LCSC C2070920
U104: AP64500SP-13 5 A buck, 3.3 V rail +3V3_S1B; SOIC-8-1EP_3.9x4.9mm_P1.27mm_EP2.29x3mm; LCSC C2070920
U105: TPS62933DRLR buck 1.0 V PCIe switch core S1; SOT-583-8; LCSC C3200405
U106: TPS62933DRLR buck 1.1 V hub core S1 (on the devic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; SOT-583-8; LCSC C3200405
U109: TI TMUXHS4212 SuperSpeed 2:1 host select, bank 1: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; Texas_RKS0020A_VQFN-20_2.5x4.5mm; LCSC C3656912
U110: TI TS3USB221A USB2 2:1 host select, bank 1: port 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; Texas_RSE0010A_UQFN-10_1.5x2mm; LCSC C128396
U111: SN74LVC32APWR quad OR, slot S1: module WiFi and B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; TSSOP-14_4.4x5mm_P0.65mm; LCSC C352974
U201: Diodes PI7C9X2G404SL PCIe 2.0 switch, slot S2: up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; LQFP-128_14x14mm_P0.4mm_EP6.0; LCSC C500767
U202: TI TUSB8041IRGCR four-port USB 3.0 hub, slot S2 (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; QFN-64-1EP_9x9mm_P0.5mm_EP4.7x4.7mm; LCSC C544686
U203: AP64500SP-13 5 A buck, 3.3 V rail +3V3_S2A; SOIC-8-1EP_3.9x4.9mm_P1.27mm_EP2.29x3mm; LCSC C2070920
U204: AP64500SP-13 5 A buck, 3.3 V rail +3V3_S2B; SOIC-8-1EP_3.9x4.9mm_P1.27mm_EP2.29x3mm; LCSC C2070920
U205: TPS62933DRLR buck 1.0 V PCIe switch core S2; SOT-583-8; LCSC C3200405
U206: TPS62933DRLR buck 1.1 V hub core S2 (on the devic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; SOT-583-8; LCSC C3200405
U209: TI TMUXHS4212 SuperSpeed 2:1 host select, bank 2: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; Texas_RKS0020A_VQFN-20_2.5x4.5mm; LCSC C3656912
U210: TI TS3USB221A USB2 2:1 host select, bank 2: port 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; Texas_RSE0010A_UQFN-10_1.5x2mm; LCSC C128396
U211: SN74LVC32APWR quad OR, slot S2: module WiFi and B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; TSSOP-14_4.4x5mm_P0.65mm; LCSC C352974
U301: Diodes PI7C9X2G404SL PCIe 2.0 switch, slot S3: up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; LQFP-128_14x14mm_P0.4mm_EP6.0; LCSC C500767
U302: TI TUSB8041IRGCR four-port USB 3.0 hub, slot S3 (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; QFN-64-1EP_9x9mm_P0.5mm_EP4.7x4.7mm; LCSC C544686
U303: AP64500SP-13 5 A buck, 3.3 V rail +3V3_S3A; SOIC-8-1EP_3.9x4.9mm_P1.27mm_EP2.29x3mm; LCSC C2070920
U304: AP64500SP-13 5 A buck, 3.3 V rail +3V3_S3B; SOIC-8-1EP_3.9x4.9mm_P1.27mm_EP2.29x3mm; LCSC C2070920
U305: TPS62933DRLR buck 1.0 V PCIe switch core S3; SOT-583-8; LCSC C3200405
U306: TPS62933DRLR buck 1.1 V hub core S3 (on the devic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; SOT-583-8; LCSC C3200405
U309: TI TMUXHS4212 SuperSpeed 2:1 host select, bank 3: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; Texas_RKS0020A_VQFN-20_2.5x4.5mm; LCSC C3656912
U310: TI TS3USB221A USB2 2:1 host select, bank 3: port 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; Texas_RSE0010A_UQFN-10_1.5x2mm; LCSC C128396
U311: SN74LVC32APWR quad OR, slot S3: module WiFi and B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; TSSOP-14_4.4x5mm_P0.65mm; LCSC C352974
Y1: 25 MHz 3225; Crystal_SMD_3225-4Pin_3.2x2.5mm; LCSC C164047
Y2, Y3, Y4: 25 MHz 3225 (CAN-FD bit timing needs a crystal, n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; Crystal_SMD_3225-4Pin_3.2x2.5mm; LCSC C164047
Y101, Y201, Y301: 24 MHz 3225; Crystal_SMD_3225-4Pin_3.2x2.5mm

Connections:
5G_OFF: Q207.1 (G), R61.1, U6.10 (IO0_6)
5G_PWROFF_n: J_M2C2.6 (~FULL_CARD_POWER_OFF), Q207.3 (D), R238.1
5G_RESET: Q208.1 (G), R62.1, U6.11 (IO0_7)
5G_RST_n: J_M2C2.67 (~RESET), Q208.3 (D)
5G_W_DIS_n: J_M2C2.8 (~W_DISABLE1), Q206.3 (D), R237.1
5G_nLED: J_M2C2.10 (GPIO_9/DAS/~DSS/~LED1), LED25.1 (K)
+1V0_S1: C126.1, C127.1, C141.1, C142.1, C143.1, C144.1, C145.1, C146.1, C148.1, L103.2, R113.1, TP22.1, U101.3 (VDDC), U101.13 (VDDCAUX), U101.14 (VDDCAUX), U101.23 (VDDC), U101.29 (VDDC), U101.31 (VDDC), U101.40 (VDDC), U101.55 (VDDC), U101.62 (VDDC), U101.65 (VDDC), U101.91 (VDDC), U101.99 (AVDD), U101.105 (AVDD), U101.108 (AVDD), U101.119 (AVDD), U101.125 (AVDD)
+1V0_S2: C226.1, C227.1, C241.1, C242.1, C243.1, C244.1, C245.1, C246.1, C248.1, L203.2, R213.1, TP26.1, U201.3 (VDDC), U201.13 (VDDCAUX), U201.14 (VDDCAUX), U201.23 (VDDC), U201.29 (VDDC), U201.31 (VDDC), U201.40 (VDDC), U201.55 (VDDC), U201.62 (VDDC), U201.65 (VDDC), U201.91 (VDDC), U201.99 (AVDD), U201.105 (AVDD), U201.108 (AVDD), U201.119 (AVDD), U201.125 (AVDD)
+1V0_S3: C326.1, C327.1, C341.1, C342.1, C343.1, C344.1, C345.1, C346.1, C348.1, L303.2, R313.1, TP30.1, U301.3 (VDDC), U301.13 (VDDCAUX), U301.14 (VDDCAUX), U301.23 (VDDC), U301.29 (VDDC), U301.31 (VDDC), U301.40 (VDDC), U301.55 (VDDC), U301.62 (VDDC), U301.65 (VDDC), U301.91 (VDDC), U301.99 (AVDD), U301.105 (AVDD), U301.108 (AVDD), U301.119 (AVDD), U301.125 (AVDD)
+1V1_S1: C131.1, C132.1, C166.1, C167.1, C168.1, C169.1, C174.1, L104.2, R115.1, TP23.1, U102.5 (VDD), U102.8 (VDD), U102.13 (VDD), U102.21 (VDD), U102.28 (VDD), U102.31 (VDD), U102.51 (VDD), U102.57 (VDD)
+1V1_S2: C231.1, C232.1, C266.1, C267.1, C268.1, C269.1, C274.1, L204.2, R215.1, TP27.1, U202.5 (VDD), U202.8 (VDD), U202.13 (VDD), U202.21 (VDD), U202.28 (VDD), U202.31 (VDD), U202.51 (VDD), U202.57 (VDD)
+1V1_S3: C331.1, C332.1, C366.1, C367.1, C368.1, C369.1, C374.1, L304.2, R315.1, TP31.1, U302.5 (VDD), U302.8 (VDD), U302.13 (VDD), U302.21 (VDD), U302.28 (VDD), U302.31 (VDD), U302.51 (VDD), U302.57 (VDD)
+1V2_KSZ: C8.1, C9.1, C18.1, C21.1, C24.1, C27.1, L2.2, R1.1, TP4.1, U1.3 (AVDDL), U1.11 (DVDDL), U1.14 (AVDDL), U1.19 (AVDDL), U1.23 (DVDDL), U1.30 (AVDDL), U1.36 (AVDDL), U1.41 (AVDDL), U1.45 (DVDDL), U1.56 (DVDDL), U1.74 (DVDDL), U1.87 (DVDDL), U1.104 (DVDDL), U1.110 (DVDDL), U1.114 (AVDDL), U1.119 (AVDDL), U1.124 (AVDDL)
+1V8_CM1: U30A.88 (CM5_1.8V), U30A.90 (CM5_1.8V)
+1V8_CM2: U31A.88 (CM5_1.8V), U31A.90 (CM5_1.8V)
+1V8_CM3: U32A.88 (CM5_1.8V), U32A.90 (CM5_1.8V)
+2V5_KSZ: C12.1, C19.1, C22.1, C25.1, C28.1, TP5.1, U1.10 (AVDDH), U1.22 (AVDDH), U1.33 (AVDDH), U1.44 (AVDDH), U1.111 (AVDDH), U1.122 (AVDDH), U1.128 (AVDDH), U27.5 (+2V5_KSZ)
+3V3_CM1: C109.1, C110.1, Q101.2 (E), Q102.1 (G), Q103.1 (G), Q104.1 (G), Q105.1 (G), R111.1, R148.1, R151.2, R154.2, R155.2, R156.2, R157.2, U30A.78 (GPIO_VREF), U30A.84 (CM5_3.3V), U30A.86 (CM5_3.3V)
+3V3_CM2: C209.1, C210.1, Q201.2 (E), Q202.1 (G), Q203.1 (G), Q204.1 (G), Q205.1 (G), R211.1, R248.1, R251.2, R254.2, R255.2, R256.2, R257.2, U31A.78 (GPIO_VREF), U31A.84 (CM5_3.3V), U31A.86 (CM5_3.3V)
+3V3_CM3: C309.1, C310.1, Q301.2 (E), Q302.1 (G), Q303.1 (G), Q304.1 (G), Q305.1 (G), R311.1, R348.1, R351.2, R354.2, R355.2, R356.2, R357.2, U32A.78 (GPIO_VREF), U32A.84 (CM5_3.3V), U32A.86 (CM5_3.3V)
+3V3_DEV: C5.1, C6.1, C13.1, C17.1, C20.1, C23.1, C26.1, C36.1, C37.1, C38.1, C40.1, C41.1, C65.1, C66.1, C67.1, C68.1, C69.1, C70.1, C71.1, C170.1, C171.1, C172.1, C173.1, C192.1, C193.1, C194.1, C197.1, C270.1, C271.1, C272.1, C273.1, C292.1, C293.1, C294.1, C297.1, C370.1, C371.1, C372.1, C373.1, C392.1, C393.1, C394.1, C397.1, C470.1, C471.1, C472.1, C473.1, C474.1, C475.1, C476.1, C477.1, C478.1, C479.1, C480.1, L1.2, R4.2, R5.1, R6.1, R7.1, R8.1, R11.2, R14.2, R21.2, R37.2, R41.2, R42.2, R44.2, R47.2, R54.2, R55.2, R56.2, R141.2, R145.2, R146.2, R158.2, R162.2, R163.2, R241.2, R245.2, R246.2, R258.2, R262.2, R263.2, R341.2, R345.2, R346.2, R358.2, R362.2, R363.2, R510.2, R513.2, TP3.1, U1.61 (VDDIO), U1.77 (VDDIO), U1.99 (VDDIO), U3.1 (VCC), U4.1 (VCC), U5.1 (VDD), U6.24 (VDD), U7.3 (A2), U7.21 (A0), U7.24 (VDD), U8.8 (+3V3_DEV), U9.2 (+3V3_DEV), U10.4 (+3V3_DEV), U10.5 (+3V3_DEV), U11.23 (VCC), U19.14 (+3V3_DEV), U20.14 (+3V3_DEV), U22.6 (VIN), U25.1 (+3V3_DEV), U27.1 (+3V3_DEV), U27.3 (+3V3_DEV), U29.5 (VBUS), U37.5 (VBUS), U70.14 (+3V3_DEV), U71.14 (+3V3_DEV), U72.14 (+3V3_DEV), U73.14 (+3V3_DEV), U74.14 (+3V3_DEV), U75.14 (+3V3_DEV), U76.14 (+3V3_DEV), U77.14 (+3V3_DEV), U78.14 (+3V3_DEV), U79.14 (+3V3_DEV), U80.14 (+3V3_DEV), U102.16 (VDD33), U102.34 (VDD33), U102.52 (VDD33), U102.63 (VDD33), U109.1 (RSVD1), U109.6 (VCC), U109.10 (RSVD2), U110.10 (VCC), U111.14 (+3V3_DEV), U202.16 (VDD33), U202.34 (VDD33), U202.52 (VDD33), U202.63 (VDD33), U209.1 (RSVD1), U209.6 (VCC), U209.10 (RSVD2), U210.10 (VCC), U211.14 (+3V3_DEV), U302.16 (VDD33), U302.34 (VDD33), U302.52 (VDD33), U302.63 (VDD33), U309.1 (RSVD1), U309.6 (VCC), U309.10 (RSVD2), U310.10 (VCC), U311.14 (+3V3_DEV)
+3V3_IOCA: C401.1, C402.1, C403.1, C404.1, C405.1, C406.1, R63.2, R65.1, U40.5 (+3V3_IOCA), U41.6 (VBAT), U41.11 (VDD), U41.20 (VREF+), U41.21 (VDDA), U41.27 (VDD), U41.50 (VDD), U41.75 (VDD), U41.100 (VDD), U42.1 (+3V3_IOCA), U43.3 (+3V3_IOCA), U44.3 (+3V3_IOCA)
+3V3_IOCB: C421.1, C422.1, C423.1, C424.1, C425.1, C426.1, R75.2, R77.1, U50.5 (+3V3_IOCB), U51.6 (VBAT), U51.11 (VDD), U51.20 (VREF+), U51.21 (VDDA), U51.27 (VDD), U51.50 (VDD), U51.75 (VDD), U51.100 (VDD), U52.1 (+3V3_IOCB), U53.3 (+3V3_IOCB), U54.3 (+3V3_IOCB)
+3V3_IOCC: C441.1, C442.1, C443.1, C444.1, C445.1, C446.1, R87.2, R89.1, U60.5 (+3V3_IOCC), U61.6 (VBAT), U61.11 (VDD), U61.20 (VREF+), U61.21 (VDDA), U61.27 (VDD), U61.50 (VDD), U61.75 (VDD), U61.100 (VDD), U62.1 (+3V3_IOCC), U63.3 (+3V3_IOCC), U64.3 (+3V3_IOCC)
+3V3_M2C1: C157.1, C158.1, J_M2C1.2 (3.3V), J_M2C1.4 (3.3V), J_M2C1.72 (3.3V), J_M2C1.74 (3.3V), R165.2, TP103.1
+3V3_M2C2: C257.1, C258.1, C520.1, C521.1, C522.1, C523.1, C524.1, C525.1, C526.1, C527.1, C528.1, C529.1, C530.1, D520.1 (K), J_M2C2.2 (3.3V), J_M2C2.4 (3.3V), J_M2C2.70 (3.3V), J_M2C2.72 (3.3V), J_M2C2.74 (3.3V), R265.2, TP203.1
+3V3_M2C3: C357.1, C358.1, J_M2C3.2 (3.3V), J_M2C3.4 (3.3V), J_M2C3.72 (3.3V), J_M2C3.74 (3.3V), R365.2, TP303.1
+3V3_S1A: C114.1, C115.1, C116.1, L101.2, R102.1, R134.2, R137.2, R138.2, R139.1, R165.1, TP20.1, TP102.1
+3V3_S1B: C121.1, C122.1, C123.1, C135.1, C136.1, C137.1, C138.1, C139.1, C140.1, C147.1, C149.1, C150.1, J_M2N1.2 (3.3V), J_M2N1.4 (3.3V), J_M2N1.12 (3.3V), J_M2N1.14 (3.3V), J_M2N1.16 (3.3V), J_M2N1.18 (3.3V), J_M2N1.70 (3.3V), J_M2N1.72 (3.3V), J_M2N1.74 (3.3V), L102.2, R107.1, R119.2, R120.2, R121.2, R123.2, R125.2, R126.2, R130.1, R131.1, R132.2, R133.2, R136.1, TP21.1, U101.1 (VDDR), U101.8 (VDDR), U101.15 (VAUX), U101.49 (VDDR), U101.64 (VDDR), U101.79 (CVDDR), U101.82 (CVDDR), U101.84 (CVDDR), U101.96 (VDDR), U101.113 (AVDDH)
+3V3_S2A: C214.1, C215.1, C216.1, L201.2, R202.1, R234.2, R237.2, R238.2, R239.1, R265.1, TP24.1, TP202.1
+3V3_S2B: C221.1, C222.1, C223.1, C235.1, C236.1, C237.1, C238.1, C239.1, C240.1, C247.1, C249.1, C250.1, J_M2N2.2 (3.3V), J_M2N2.4 (3.3V), J_M2N2.12 (3.3V), J_M2N2.14 (3.3V), J_M2N2.16 (3.3V), J_M2N2.18 (3.3V), J_M2N2.70 (3.3V), J_M2N2.72 (3.3V), J_M2N2.74 (3.3V), L202.2, R207.1, R219.2, R220.2, R221.2, R223.2, R225.2, R226.2, R230.1, R231.1, R232.2, R233.2, R236.1, TP25.1, U201.1 (VDDR), U201.8 (VDDR), U201.15 (VAUX), U201.49 (VDDR), U201.64 (VDDR), U201.79 (CVDDR), U201.82 (CVDDR), U201.84 (CVDDR), U201.96 (VDDR), U201.113 (AVDDH)
+3V3_S3A: C314.1, C315.1, C316.1, L301.2, R302.1, R334.2, R337.2, R338.2, R339.1, R365.1, TP28.1, TP302.1
+3V3_S3B: C321.1, C322.1, C323.1, C335.1, C336.1, C337.1, C338.1, C339.1, C340.1, C347.1, C349.1, C350.1, J_M2N3.2 (3.3V), J_M2N3.4 (3.3V), J_M2N3.12 (3.3V), J_M2N3.14 (3.3V), J_M2N3.16 (3.3V), J_M2N3.18 (3.3V), J_M2N3.70 (3.3V), J_M2N3.72 (3.3V), J_M2N3.74 (3.3V), J_SPI3.1, L302.2, R25.2, R307.1, R319.2, R320.2, R321.2, R323.2, R325.2, R326.2, R330.1, R331.1, R332.2, R333.2, R336.1, TP29.1, U301.1 (VDDR), U301.8 (VDDR), U301.15 (VAUX), U301.49 (VDDR), U301.64 (VDDR), U301.79 (CVDDR), U301.82 (CVDDR), U301.84 (CVDDR), U301.96 (VDDR), U301.113 (AVDDH)
+3V3_ZB: C53.1, C54.1, C55.1, J_ZBDBG1.1, J_ZBDBG2.1, R28.2, R29.2, R30.2, R31.2, TP17.1, U13.20 (+3V3_ZB), U14.20 (+3V3_ZB), U22.1 (VOUT)
+5V_CAM: C64.1, J_CAM.1, U28.1 (OUT), U34.5 (VBUS)
+5V_DEV: C1.1, C2.1, C4.1, C7.1, C57.1, C62.1, C130.1, C230.1, C330.1, C400.1, C420.1, C440.1, D1.1 (K), F1.1, F2.1, F3.1, J_5V_DEV.1, R38.1, R45.1, R66.1, R78.1, R90.1, R143.1, R243.1, R343.1, TP2.1, U15.7 (VREGIN), U15.8 (VBUS), U16.7 (VREGIN), U16.8 (VBUS), U17.7 (VREGIN), U17.8 (VBUS), U18.7 (VREGIN), U18.8 (VBUS), U21.6 (VIN), U23.4 (+5V_DEV), U24.4 (+5V_DEV), U25.2 (+5V_DEV), U25.3 (+5V_DEV), U26.2 (+5V_DEV), U26.3 (+5V_DEV), U28.5 (IN), U40.1 (+5V_DEV), U50.1 (+5V_DEV), U60.1 (+5V_DEV), U106.2 (+5V_DEV), U106.3 (+5V_DEV), U206.2 (+5V_DEV), U206.3 (+5V_DEV), U306.2 (+5V_DEV), U306.3 (+5V_DEV)
+5V_HDMI: C39.1, F2.2, J_HDMI.18 (+5V), R17.2, R18.2
+5V_LIME: C58.1, J_LIME.1 (VBUS), TP14.1, U23.5 (+5V_LIME), U33.5 (VBUS)
+5V_LORA: C46.1, C47.1, TP16.1, U12.9 (VCC), U12.10 (VCC), U21.1 (VOUT)
+5V_RB: C63.1, J_RB9704.15, TP15.1, U24.5 (+5V_RB)
+5V_S1: C101.1, C102.1, C103.1, C104.1, C105.1, C106.1, C107.1, C108.1, C112.1, C113.1, C119.1, C120.1, C125.1, D101.1 (K), J_5V_S1.1, J_FAN1.1, R101.1, U30A.77 (5V), U30A.79 (5V), U30A.81 (5V), U30A.83 (5V), U30A.85 (5V), U30A.87 (5V), U103.2 (+5V_S1), U104.2 (+5V_S1), U105.3 (+5V_S1)
+5V_S2: C201.1, C202.1, C203.1, C204.1, C205.1, C206.1, C207.1, C208.1, C212.1, C213.1, C219.1, C220.1, C225.1, D201.1 (K), J_5V_S2.1, J_FAN2.1, R201.1, U31A.77 (5V), U31A.79 (5V), U31A.81 (5V), U31A.83 (5V), U31A.85 (5V), U31A.87 (5V), U203.2 (+5V_S2), U204.2 (+5V_S2), U205.3 (+5V_S2)
+5V_S3: C301.1, C302.1, C303.1, C304.1, C305.1, C306.1, C307.1, C308.1, C312.1, C313.1, C319.1, C320.1, C325.1, D301.1 (K), J_5V_S3.1, J_FAN3.1, R301.1, U32A.77 (5V), U32A.79 (5V), U32A.81 (5V), U32A.83 (5V), U32A.85 (5V), U32A.87 (5V), U303.2 (+5V_S3), U304.2 (+5V_S3), U305.3 (+5V_S3)
+54V_POE: C34.1, C35.1, D2.1 (K), J_54V.1, R13.1, TP12.1, U5.28 (VPWR)
BANK1_UPD_N: U102.54 (USB_DM_UP), U110.7 (Dn)
BANK1_UPD_P: U102.53 (USB_DP_UP), U110.8 (Dp)
BANK1_UPRX_N: C160.1, U102.56 (USB_SSTXM_UP)
BANK1_UPRX_P: C159.1, U102.55 (USB_SSTXP_UP)
BANK1_UPTX_N: U102.59 (USB_SSRXM_UP), U109.4 (A0n)
BANK1_UPTX_P: U102.58 (USB_SSRXP_UP), U109.3 (A0p)
BANK2_UPD_N: U202.54 (USB_DM_UP), U210.7 (Dn)
BANK2_UPD_P: U202.53 (USB_DP_UP), U210.8 (Dp)
BANK2_UPRX_N: C260.1, U202.56 (USB_SSTXM_UP)
BANK2_UPRX_P: C259.1, U202.55 (USB_SSTXP_UP)
BANK2_UPTX_N: U202.59 (USB_SSRXM_UP), U209.4 (A0n)
BANK2_UPTX_P: U202.58 (USB_SSRXP_UP), U209.3 (A0p)
BANK3_UPD_N: U302.54 (USB_DM_UP), U310.7 (Dn)
BANK3_UPD_P: U302.53 (USB_DP_UP), U310.8 (Dp)
BANK3_UPRX_N: C360.1, U302.56 (USB_SSTXM_UP)
BANK3_UPRX_P: C359.1, U302.55 (USB_SSTXP_UP)
BANK3_UPTX_N: U302.59 (USB_SSRXM_UP), U309.4 (A0n)
BANK3_UPTX_P: U302.58 (USB_SSRXP_UP), U309.3 (A0p)
BOB: C33.1, R9.2, R10.2
BOE1_n: R161.1, TP507.1, U80.3 (BOE1_n), U109.2 (OEn), U110.6 (OEn)
BOE2_n: R261.1, TP508.1, U80.6 (BOE2_n), U209.2 (OEn), U210.6 (OEn)
BOE3_n: R361.1, TP509.1, U80.8 (BOE3_n), U309.2 (OEn), U310.6 (OEn)
BSEL1: R160.1, R474.1, TP504.1, U41.38 (PE8), U51.38 (PE8), U61.38 (PE8), U76.6 (BSEL1), U80.1 (BSEL1), U109.9 (SEL), U110.9 (S)
BSEL1_D: C481.1, R474.2, U80.2 (BSEL1_D)
BSEL2: R260.1, R475.1, TP505.1, U41.39 (PE9), U51.39 (PE9), U61.39 (PE9), U76.11 (BSEL2), U80.4 (BSEL2), U209.9 (SEL), U210.9 (S)
BSEL2_D: C482.1, R475.2, U80.5 (BSEL2_D)
BSEL3: R360.1, R476.1, TP506.1, U41.40 (PE10), U51.40 (PE10), U61.40 (PE10), U77.6 (BSEL3), U80.10 (BSEL3), U309.9 (SEL), U310.9 (S)
BSEL3_D: C483.1, R476.2, U80.9 (BSEL3_D)
BT_nDIS1: Q110.3 (D), U30A.91 (BT_nDisable)
BT_nDIS1_KILL: Q110.1 (G), R174.1, U111.6 (BT_nDIS1_KILL)
BT_nDIS1_OFF: R163.1, U6.16 (IO1_3), U111.4 (BT_nDIS1_OFF)
BT_nDIS2: Q210.3 (D), U31A.91 (BT_nDisable)
BT_nDIS2_KILL: Q210.1 (G), R274.1, U211.6 (BT_nDIS2_KILL)
BT_nDIS2_OFF: R263.1, U6.17 (IO1_4), U211.4 (BT_nDIS2_OFF)
BT_nDIS3: Q310.3 (D), U32A.91 (BT_nDisable)
BT_nDIS3_KILL: Q310.1 (G), R374.1, U311.6 (BT_nDIS3_KILL)
BT_nDIS3_OFF: R363.1, U6.18 (IO1_5), U311.4 (BT_nDIS3_OFF)
CAM_DM: J_CAM.2, U34.3 (I/O2), U34.4 (I/O2), U102.18 (USB_DM_DN3)
CAM_DP: J_CAM.3, U34.1 (I/O1), U34.6 (I/O1), U102.17 (USB_DP_DN3)
CAM_EN: R48.1, U6.9 (IO0_5), U28.4 (EN)
CAM_FLT: R47.1, U7.6 (IO0_2), U28.3 (~FLT)
CANH_A: R504.1, R508.2, TP535.1, U53.7 (CANH_A), U63.7 (CANH_A)
CANH_A1: R470.1, R508.1, U43.7 (CANH_A1)
CANH_B: R506.1, R511.2, TP537.1, U54.7 (CANH_B), U64.7 (CANH_B)
CANH_B1: R472.1, R511.1, U44.7 (CANH_B1)
CANL_A: R505.2, R509.2, TP536.1, U53.6 (CANL_A), U63.6 (CANL_A)
CANL_A1: R471.2, R509.1, U43.6 (CANL_A1)
CANL_B: R507.2, R512.2, TP538.1, U54.6 (CANL_B), U64.6 (CANL_B)
CANL_B1: R473.2, R512.1, U44.6 (CANL_B1)
CANT2_A: C506.1, R504.2, R505.1
CANT2_B: C507.1, R506.2, R507.1
CANT_A: C460.1, R470.2, R471.1
CANT_B: C461.1, R472.2, R473.1
CARD1_CLKREQ_n: J_M2C1.53 (~CLKREQ0), R134.1
CARD1_CLK_N: J_M2C1.49 (REFCLKn0), R184.2, R186.1
CARD1_CLK_P: J_M2C1.47 (REFCLKp0), R183.2, R185.1
CARD1_CLK_SRC_N: R184.1, U101.77 (REFCLKO_N2)
CARD1_CLK_SRC_P: R183.1, U101.78 (REFCLKO_P2)
CARD1_RX_N: C156.2, J_M2C1.37 (PETn0)
CARD1_RX_P: C155.2, J_M2C1.35 (PETp0)
CARD1_RX_SW_N: C156.1, U101.107 (PETN2)
CARD1_RX_SW_P: C155.1, U101.106 (PETP2)
CARD1_TX_N: J_M2C1.43 (PERn0), U101.103 (PERN2)
CARD1_TX_P: J_M2C1.41 (PERp0), U101.102 (PERP2)
CARD2_CLKREQ_n: J_M2C2.52 (~CLKREQ), R234.1
CARD2_CLK_N: J_M2C2.53 (REFCLKn), R284.2, R286.1
CARD2_CLK_P: J_M2C2.55 (REFCLKp), R283.2, R285.1
CARD2_CLK_SRC_N: R284.1, U201.77 (REFCLKO_N2)
CARD2_CLK_SRC_P: R283.1, U201.78 (REFCLKO_P2)
CARD2_RX_N: C256.2, J_M2C2.47 (PETn0/SATA-A-)
CARD2_RX_P: C255.2, J_M2C2.49 (PETp0/SATA-A+)
CARD2_RX_SW_N: C256.1, U201.107 (PETN2)
CARD2_RX_SW_P: C255.1, U201.106 (PETP2)
CARD2_TX_N: J_M2C2.41 (PERn0/SATA-B+), U201.103 (PERN2)
CARD2_TX_P: J_M2C2.43 (PERp0/SATA-B-), U201.102 (PERP2)
CARD3_CLKREQ_n: J_M2C3.53 (~CLKREQ0), R334.1
CARD3_CLK_N: J_M2C3.49 (REFCLKn0), R384.2, R386.1
CARD3_CLK_P: J_M2C3.47 (REFCLKp0), R383.2, R385.1
CARD3_CLK_SRC_N: R384.1, U301.77 (REFCLKO_N2)
CARD3_CLK_SRC_P: R383.1, U301.78 (REFCLKO_P2)
CARD3_RX_N: C356.2, J_M2C3.37 (PETn0)
CARD3_RX_P: C355.2, J_M2C3.35 (PETp0)
CARD3_RX_SW_N: C356.1, U301.107 (PETN2)
CARD3_RX_SW_P: C355.1, U301.106 (PETP2)
CARD3_TX_N: J_M2C3.43 (PERn0), U301.103 (PERN2)
CARD3_TX_P: J_M2C3.41 (PERp0), U301.102 (PERP2)
CC1_F1: J_FLASH1.A5 (CC1), R152.1
CC1_F2: J_FLASH2.A5 (CC1), R252.1
CC1_F3: J_FLASH3.A5 (CC1), R352.1
CC2_F1: J_FLASH1.B5 (CC2), R153.1
CC2_F2: J_FLASH2.B5 (CC2), R253.1
CC2_F3: J_FLASH3.B5 (CC2), R353.1
DEV_BST: C3.1, U25.6 (DEV_BST)
DEV_SW: C3.2, L1.1, U25.5 (DEV_SW)
E22_CT: C45.1, U21.3 (CT)
E22_EN: R516.1, U19.11 (E22_EN), U21.5 (EN/UVLO)
E72_CT: C52.1, U22.3 (CT)
E72_EN: R517.1, U20.3 (E72_EN), U22.5 (EN/UVLO)
EMCON_HW: J_AB1.15, J_PANEL.8, Q11.1 (G), R58.1, TP7.1, U19.1 (EMCON_HW), U19.9 (EMCON_HW), U19.12 (EMCON_HW), U20.1 (EMCON_HW), U41.33 (PC5), U51.33 (PC5), U61.33 (PC5)
EMCON_ON: Q11.3 (D), Q106.1 (G), Q111.1 (G), Q206.1 (G), Q306.1 (G), Q311.1 (G), R513.1, U111.2 (EMCON_ON), U111.5 (EMCON_ON), U211.2 (EMCON_ON), U211.5 (EMCON_ON), U311.2 (EMCON_ON), U311.5 (EMCON_ON)
EN33_S1: R111.2, R112.1, U104.3 (EN33_S1), U105.2 (EN33_S1)
EN33_S2: R211.2, R212.1, U204.3 (EN33_S2), U205.2 (EN33_S2)
EN33_S3: R311.2, R312.1, U304.3 (EN33_S3), U305.2 (EN33_S3)
ETH1_P0_N: C176.1, U30A.10 (Ethernet_Pair0_N)
ETH1_P0_P: C175.1, U30A.12 (Ethernet_Pair0_P)
ETH1_P1_N: C178.1, U30A.6 (Ethernet_Pair1_N)
ETH1_P1_P: C177.1, U30A.4 (Ethernet_Pair1_P)
ETH1_P2_N: C180.1, U30A.9 (Ethernet_Pair2_N)
ETH1_P2_P: C179.1, U30A.11 (Ethernet_Pair2_P)
ETH1_P3_N: C182.1, U30A.5 (Ethernet_Pair3_N)
ETH1_P3_P: C181.1, U30A.3 (Ethernet_Pair3_P)
ETH2_P0_N: C276.1, U31A.10 (Ethernet_Pair0_N)
ETH2_P0_P: C275.1, U31A.12 (Ethernet_Pair0_P)
ETH2_P1_N: C278.1, U31A.6 (Ethernet_Pair1_N)
ETH2_P1_P: C277.1, U31A.4 (Ethernet_Pair1_P)
ETH2_P2_N: C280.1, U31A.9 (Ethernet_Pair2_N)
ETH2_P2_P: C279.1, U31A.11 (Ethernet_Pair2_P)
ETH2_P3_N: C282.1, U31A.5 (Ethernet_Pair3_N)
ETH2_P3_P: C281.1, U31A.3 (Ethernet_Pair3_P)
ETH3_P0_N: C376.1, U32A.10 (Ethernet_Pair0_N)
ETH3_P0_P: C375.1, U32A.12 (Ethernet_Pair0_P)
ETH3_P1_N: C378.1, U32A.6 (Ethernet_Pair1_N)
ETH3_P1_P: C377.1, U32A.4 (Ethernet_Pair1_P)
ETH3_P2_N: C380.1, U32A.9 (Ethernet_Pair2_N)
ETH3_P2_P: C379.1, U32A.11 (Ethernet_Pair2_P)
ETH3_P3_N: C382.1, U32A.5 (Ethernet_Pair3_N)
ETH3_P3_P: C381.1, U32A.3 (Ethernet_Pair3_P)
EXP_INT: J_AB1.13, J_PANEL.6, R56.1, U1.94 (INTRP_N), U5.6 (INT), U6.1 (~INT), U7.1 (~INT), U9.3 (EXP_INT), U10.3 (EXP_INT)
EXP_SPARE1: TP41.1, U7.9 (IO0_5)
EXP_SPARE2: TP42.1, U7.10 (IO0_6)
EXP_SPARE3: TP43.1, U7.11 (IO0_7)
EXP_SPARE4: TP44.1, U7.13 (IO1_0)
EXP_SPARE5: TP45.1, U7.14 (IO1_1)
EXP_SPARE6: TP46.1, U7.15 (IO1_2)
EXP_SPARE7: TP47.1, U7.16 (IO1_3)
EXP_SPARE8: TP48.1, U7.17 (IO1_4)
EXP_SPARE9: TP49.1, U7.18 (IO1_5)
EXP_SPARE10: TP50.1, U7.19 (IO1_6)
EXP_SPARE11: TP51.1, U7.20 (IO1_7)
FAN_PWM1: J_FAN1.4, R151.1, U30A.19 (Fan_PWM)
FAN_PWM2: J_FAN2.4, R251.1, U31A.19 (Fan_PWM)
FAN_PWM3: J_FAN3.4, R351.1, U32A.19 (Fan_PWM)
FAN_TACHO1: J_FAN1.3, U30A.16 (Fan_Tacho)
FAN_TACHO2: J_FAN2.3, U31A.16 (Fan_Tacho)
FAN_TACHO3: J_FAN3.3, U32A.16 (Fan_Tacho)
GND: BT1.2 (-), C1.2, C2.2, C4.2, C5.2, C6.2, C7.2, C8.2, C9.2, C11.2, C12.2, C13.2, C14.2, C15.2, C16.2, C17.2, C18.2, C19.2, C20.2, C21.2, C22.2, C23.2, C24.2, C25.2, C26.2, C27.2, C28.2, C29.2, C30.2, C31.2, C32.2, C33.2, C34.2, C35.2, C36.2, C37.2, C38.2, C39.2, C40.2, C41.2, C43.2, C44.2, C45.2, C46.2, C47.2, C48.2, C49.2, C50.2, C51.2, C52.2, C53.2, C54.2, C55.2, C56.2, C57.2, C58.2, C59.2, C60.2, C61.2, C62.2, C63.2, C64.2, C65.2, C66.2, C67.2, C68.2, C69.2, C70.2, C71.2, C101.2, C102.2, C103.2, C104.2, C105.2, C106.2, C107.2, C108.2, C109.2, C110.2, C112.2, C113.2, C114.2, C115.2, C116.2, C117.2, C119.2, C120.2, C121.2, C122.2, C123.2, C124.2, C125.2, C126.2, C127.2, C129.2, C130.2, C131.2, C132.2, C134.2, C135.2, C136.2, C137.2, C138.2, C139.2, C140.2, C141.2, C142.2, C143.2, C144.2, C145.2, C146.2, C147.2, C148.2, C149.2, C150.2, C157.2, C158.2, C163.2, C164.2, C165.2, C166.2, C167.2, C168.2, C169.2, C170.2, C171.2, C172.2, C173.2, C174.2, C192.2, C193.2, C194.2, C197.2, C201.2, C202.2, C203.2, C204.2, C205.2, C206.2, C207.2, C208.2, C209.2, C210.2, C212.2, C213.2, C214.2, C215.2, C216.2, C217.2, C219.2, C220.2, C221.2, C222.2, C223.2, C224.2, C225.2, C226.2, C227.2, C229.2, C230.2, C231.2, C232.2, C234.2, C235.2, C236.2, C237.2, C238.2, C239.2, C240.2, C241.2, C242.2, C243.2, C244.2, C245.2, C246.2, C247.2, C248.2, C249.2, C250.2, C257.2, C258.2, C263.2, C264.2, C265.2, C266.2, C267.2, C268.2, C269.2, C270.2, C271.2, C272.2, C273.2, C274.2, C283.2, C284.2, C286.2, C287.2, C288.2, C289.2, C290.2, C291.2, C292.2, C293.2, C294.2, C297.2, C298.2, C301.2, C302.2, C303.2, C304.2, C305.2, C306.2, C307.2, C308.2, C309.2, C310.2, C312.2, C313.2, C314.2, C315.2, C316.2, C317.2, C319.2, C320.2, C321.2, C322.2, C323.2, C324.2, C325.2, C326.2, C327.2, C329.2, C330.2, C331.2, C332.2, C334.2, C335.2, C336.2, C337.2, C338.2, C339.2, C340.2, C341.2, C342.2, C343.2, C344.2, C345.2, C346.2, C347.2, C348.2, C349.2, C350.2, C357.2, C358.2, C363.2, C364.2, C365.2, C366.2, C367.2, C368.2, C369.2, C370.2, C371.2, C372.2, C373.2, C374.2, C392.2, C393.2, C394.2, C397.2, C400.2, C401.2, C402.2, C403.2, C404.2, C405.2, C406.2, C407.2, C408.2, C409.2, C410.2, C411.2, C420.2, C421.2, C422.2, C423.2, C424.2, C425.2, C426.2, C427.2, C428.2, C429.2, C430.2, C431.2, C440.2, C441.2, C442.2, C443.2, C444.2, C445.2, C446.2, C447.2, C448.2, C449.2, C450.2, C451.2, C460.2, C461.2, C470.2, C471.2, C472.2, C473.2, C474.2, C475.2, C476.2, C477.2, C478.2, C479.2, C480.2, C481.2, C482.2, C483.2, C506.2, C507.2, C520.2, C521.2, C522.2, C523.2, C524.2, C525.2, C526.2, C527.2, C528.2, C529.2, C530.2, D1.2 (A), D2.2 (A), D101.2 (A), D201.2 (A), D301.2 (A), D520.2 (A), J_5V_DEV.2, J_5V_S1.2, J_5V_S2.2, J_5V_S3.2, J_54V.2, J_AB1.3, J_AB1.4, J_AB1.5, J_AB1.6, J_AB1.7, J_AB1.8, J_AB1.22, J_AB1.23, J_AB1.24, J_AB2.3, J_AB2.4, J_AB2.5, J_AB2.6, J_AB2.7, J_AB2.8, J_AB2.9, J_AB2.10, J_CAM.4, J_DBG1.1, J_DBG2.1, J_DBG3.1, J_ETH.SH, J_FAN1.2, J_FAN2.2, J_FAN3.2, J_FLASH1.A1 (GND), J_FLASH1.A12 (GND), J_FLASH1.B1 (GND), J_FLASH1.B12 (GND), J_FLASH1.S1 (SHIELD), J_FLASH2.A1 (GND), J_FLASH2.A12 (GND), J_FLASH2.B1 (GND), J_FLASH2.B12 (GND), J_FLASH2.S1 (SHIELD), J_FLASH3.A1 (GND), J_FLASH3.A12 (GND), J_FLASH3.B1 (GND), J_FLASH3.B12 (GND), J_FLASH3.S1 (SHIELD), J_GNSS1.2 (Ext), J_GNSS2.1, J_HDMI.2 (D2S), J_HDMI.5 (D1S), J_HDMI.8 (D0S), J_HDMI.11 (CKS), J_HDMI.17 (GND), J_HDMI.SH, J_IOCOFF_A.2, J_IOCOFF_B.2, J_IOCOFF_C.2, J_LIME.4 (GND), J_LIME.7 (DRAIN), J_LIME.10 (SHIELD), J_LORA1.2 (Ext), J_M2C1.1 (GND), J_M2C1.7 (GND), J_M2C1.18 (GND), J_M2C1.33 (GND), J_M2C1.39 (GND), J_M2C1.45 (GND), J_M2C1.51 (GND), J_M2C1.57 (GND), J_M2C1.63 (GND), J_M2C1.69 (GND), J_M2C1.75 (GND), J_M2C2.3 (GND), J_M2C2.5 (GND), J_M2C2.11 (GND), J_M2C2.27 (GND), J_M2C2.33 (GND), J_M2C2.39 (GND), J_M2C2.45 (GND), J_M2C2.51 (GND), J_M2C2.57 (GND), J_M2C2.71 (GND), J_M2C2.73 (GND), J_M2C3.1 (GND), J_M2C3.7 (GND), J_M2C3.18 (GND), J_M2C3.33 (GND), J_M2C3.39 (GND), J_M2C3.45 (GND), J_M2C3.51 (GND), J_M2C3.57 (GND), J_M2C3.63 (GND), J_M2C3.69 (GND), J_M2C3.75 (GND), J_M2N1.1 (GND), J_M2N1.3 (GND), J_M2N1.9 (GND), J_M2N1.15 (GND), J_M2N1.21 (GND), J_M2N1.27 (GND), J_M2N1.33 (GND), J_M2N1.39 (GND), J_M2N1.45 (GND), J_M2N1.51 (GND), J_M2N1.57 (GND), J_M2N1.71 (GND), J_M2N1.73 (GND), J_M2N1.75 (GND), J_M2N2.1 (GND), J_M2N2.3 (GND), J_M2N2.9 (GND), J_M2N2.15 (GND), J_M2N2.21 (GND), J_M2N2.27 (GND), J_M2N2.33 (GND), J_M2N2.39 (GND), J_M2N2.45 (GND), J_M2N2.51 (GND), J_M2N2.57 (GND), J_M2N2.71 (GND), J_M2N2.73 (GND), J_M2N2.75 (GND), J_M2N3.1 (GND), J_M2N3.3 (GND), J_M2N3.9 (GND), J_M2N3.15 (GND), J_M2N3.21 (GND), J_M2N3.27 (GND), J_M2N3.33 (GND), J_M2N3.39 (GND), J_M2N3.45 (GND), J_M2N3.51 (GND), J_M2N3.57 (GND), J_M2N3.71 (GND), J_M2N3.73 (GND), J_M2N3.75 (GND), J_PANEL.3, J_PANEL.9, J_PANEL.14, J_PANEL.17, J_QMX.4, J_RB9704.1, J_RB9704.4, J_RB9704.10, J_RB9704.16, J_RPIBOOT1.2, J_RPIBOOT2.2, J_RPIBOOT3.2, J_SIM1.5 (GND), J_SIM1.SH, J_SIM2.5 (GND), J_SIM2.SH, J_SPI3.2, J_W1A.2 (Ext), J_W1B.2 (Ext), J_W3A.2 (Ext), J_W3B.2 (Ext), J_WOA.2 (Ext), J_WOB.2 (Ext), J_ZBDBG1.2, J_ZBDBG2.2, LED6.1 (K), LED7.1 (K), LED8.1 (K), LED9.1 (K), LED11.1 (K), LED17.1 (K), LED21.1 (K), LED27.1 (K), LED31.1 (K), LED37.1 (K), Q2.2 (S), Q3.2 (S), Q4.2 (S), Q5.2 (S), Q10.2 (S), Q11.2 (S), Q106.2 (S), Q109.2 (S), Q110.2 (S), Q111.2 (S), Q206.2 (S), Q207.2 (S), Q208.2 (S), Q209.2 (S), Q210.2 (S), Q306.2 (S), Q309.2 (S), Q310.2 (S), Q311.2 (S), R2.2, R3.2, R12.2, R15.2, R16.2, R20.2, R22.2, R36.2, R39.2, R43.2, R46.2, R48.2, R49.2, R50.2, R51.2, R52.2, R53.2, R57.2, R58.2, R59.2, R60.2, R61.2, R62.2, R64.2, R76.2, R88.2, R103.2, R104.2, R106.2, R108.2, R109.2, R112.2, R114.2, R116.2, R117.2, R118.2, R122.2, R124.2, R127.2, R128.2, R129.2, R135.2, R142.2, R144.2, R152.2, R153.2, R160.2, R161.2, R173.2, R174.2, R177.2, R178.2, R181.2, R182.2, R185.2, R186.2, R203.2, R204.2, R206.2, R208.2, R209.2, R212.2, R214.2, R216.2, R217.2, R218.2, R222.2, R224.2, R227.2, R228.2, R229.2, R235.2, R242.2, R244.2, R252.2, R253.2, R260.2, R261.2, R273.2, R274.2, R277.2, R278.2, R281.2, R282.2, R285.2, R286.2, R303.2, R304.2, R306.2, R308.2, R309.2, R312.2, R314.2, R316.2, R317.2, R318.2, R322.2, R324.2, R327.2, R328.2, R329.2, R335.2, R342.2, R344.2, R352.2, R353.2, R360.2, R361.2, R373.2, R374.2, R377.2, R378.2, R381.2, R382.2, R385.2, R386.2, R477.2, R478.2, R479.2, R480.2, R481.2, R482.2, R483.2, R484.2, R485.2, R486.2, R487.2, R488.2, R489.2, R490.2, R491.2, R492.2, R493.2, R494.2, R495.2, R496.2, R497.2, R498.2, R499.2, R500.2, R514.2, R515.2, R516.2, R517.2, TP101.1, TP201.1, TP301.1, TP501.1, TP502.1, TP503.1, U1.46 (GND), U1.47 (GND), U1.84 (GND), U1.107 (GND), U1.109 (GND), U1.123 (GND), U1.129 (E_PAD), U3.43 (GND), U4.43 (GND), U5.7 (DGND), U5.8 (SEN3), U5.11 (KSENSB), U5.12 (SEN4), U5.18 (KSENSA), U5.19 (SEN2), U5.22 (AGND), U6.2 (A1), U6.3 (A2), U6.12 (VSS), U6.21 (A0), U7.2 (A1), U7.12 (VSS), U8.4 (GND), U9.5 (GND), U10.2 (GND), U10.7 (GND), U11.10 (GND), U11.12 (GND), U11.13 (GND), U11.24 (GND), U11.25 (GND), U11.26 (GND), U11.27 (GND), U11.28 (GND), U11.29 (GND), U11.30 (GND), U11.31 (GND), U11.32 (GND), U11.33 (GND), U11.34 (GND), U11.35 (GND), U11.36 (GND), U11.37 (GND), U11.38 (GND), U11.39 (GND), U11.40 (GND), U11.41 (GND), U11.42 (GND), U11.43 (GND), U11.44 (GND), U11.45 (GND), U11.46 (GND), U11.47 (GND), U11.48 (GND), U11.49 (GND), U11.50 (GND), U11.51 (GND), U11.52 (GND), U11.53 (GND), U11.54 (GND), U11.55 (GND), U11.56 (GND), U11.57 (GND), U11.58 (GND), U11.59 (GND), U11.60 (GND), U11.61 (GND), U11.62 (GND), U11.63 (GND), U11.64 (GND), U11.65 (GND), U11.66 (GND), U11.67 (GND), U11.68 (GND), U11.69 (GND), U11.70 (GND), U11.71 (GND), U11.72 (GND), U11.73 (GND), U11.74 (GND), U11.75 (GND), U11.76 (GND), U11.77 (GND), U11.78 (GND), U11.79 (GND), U12.1 (GND), U12.2 (GND), U12.3 (GND), U12.4 (GND), U12.5 (GND), U12.11 (GND), U12.12 (GND), U12.20 (GND), U12.22 (GND), U13.1 (GND), U13.11 (GND), U13.12 (GND), U13.19 (GND), U13.23 (GND), U13.34 (GND), U14.1 (GND), U14.11 (GND), U14.12 (GND), U14.19 (GND), U14.23 (GND), U14.34 (GND), U15.3 (GND), U15.29 (GND), U16.3 (GND), U16.29 (GND), U17.3 (GND), U17.29 (GND), U18.3 (GND), U18.29 (GND), U19.7 (GND), U20.4 (GND), U20.5 (GND), U20.7 (GND), U20.9 (GND), U20.10 (GND), U20.12 (GND), U20.13 (GND), U21.4 (GND), U21.7 (GND), U22.4 (GND), U22.7 (GND), U23.1 (GND), U23.9 (GND), U24.1 (GND), U24.9 (GND), U25.4 (GND), U26.4 (GND), U27.2 (GND), U28.2 (GND), U29.2 (GND), U30A.1 (GND), U30A.2 (GND), U30A.7 (GND), U30A.8 (GND), U30A.13 (GND), U30A.14 (GND), U30A.22 (GND), U30A.23 (GND), U30A.32 (GND), U30A.33 (GND), U30A.42 (GND), U30A.43 (GND), U30A.52 (GND), U30A.53 (GND), U30A.59 (GND), U30A.60 (GND), U30A.65 (GND), U30A.66 (GND), U30A.71 (GND), U30A.74 (GND), U30A.98 (GND), U30B.107 (GND), U30B.108 (GND), U30B.113 (GND), U30B.114 (GND), U30B.119 (GND), U30B.120 (GND), U30B.125 (GND), U30B.126 (GND), U30B.131 (GND), U30B.132 (GND), U30B.137 (GND), U30B.138 (GND), U30B.144 (GND), U30B.150 (GND), U30B.155 (GND), U30B.156 (GND), U30B.161 (GND), U30B.162 (GND), U30B.167 (GND), U30B.168 (GND), U30B.173 (GND), U30B.174 (GND), U30B.179 (GND), U30B.180 (GND), U30B.185 (GND), U30B.186 (GND), U30B.191 (GND), U30B.192 (GND), U30B.197 (GND), U30B.198 (GND), U31A.1 (GND), U31A.2 (GND), U31A.7 (GND), U31A.8 (GND), U31A.13 (GND), U31A.14 (GND), U31A.22 (GND), U31A.23 (GND), U31A.32 (GND), U31A.33 (GND), U31A.42 (GND), U31A.43 (GND), U31A.52 (GND), U31A.53 (GND), U31A.59 (GND), U31A.60 (GND), U31A.65 (GND), U31A.66 (GND), U31A.71 (GND), U31A.74 (GND), U31A.98 (GND), U31B.107 (GND), U31B.108 (GND), U31B.113 (GND), U31B.114 (GND), U31B.119 (GND), U31B.120 (GND), U31B.125 (GND), U31B.126 (GND), U31B.131 (GND), U31B.132 (GND), U31B.137 (GND), U31B.138 (GND), U31B.144 (GND), U31B.150 (GND), U31B.155 (GND), U31B.156 (GND), U31B.161 (GND), U31B.162 (GND), U31B.167 (GND), U31B.168 (GND), U31B.173 (GND), U31B.174 (GND), U31B.179 (GND), U31B.180 (GND), U31B.185 (GND), U31B.186 (GND), U31B.191 (GND), U31B.192 (GND), U31B.197 (GND), U31B.198 (GND), U32A.1 (GND), U32A.2 (GND), U32A.7 (GND), U32A.8 (GND), U32A.13 (GND), U32A.14 (GND), U32A.22 (GND), U32A.23 (GND), U32A.32 (GND), U32A.33 (GND), U32A.42 (GND), U32A.43 (GND), U32A.52 (GND), U32A.53 (GND), U32A.59 (GND), U32A.60 (GND), U32A.65 (GND), U32A.66 (GND), U32A.71 (GND), U32A.74 (GND), U32A.98 (GND), U32B.107 (GND), U32B.108 (GND), U32B.113 (GND), U32B.114 (GND), U32B.119 (GND), U32B.120 (GND), U32B.125 (GND), U32B.126 (GND), U32B.131 (GND), U32B.132 (GND), U32B.137 (GND), U32B.138 (GND), U32B.144 (GND), U32B.150 (GND), U32B.155 (GND), U32B.156 (GND), U32B.161 (GND), U32B.162 (GND), U32B.167 (GND), U32B.168 (GND), U32B.173 (GND), U32B.174 (GND), U32B.179 (GND), U32B.180 (GND), U32B.185 (GND), U32B.186 (GND), U32B.191 (GND), U32B.192 (GND), U32B.197 (GND), U32B.198 (GND), U33.2 (GND), U34.2 (GND), U35.2 (GND), U37.2 (GND), U40.2 (GND), U41.10 (VSS), U41.19 (VSSA), U41.26 (VSS), U41.49 (VSS), U41.74 (VSS), U41.99 (VSS), U42.5 (GND), U43.2 (GND), U43.8 (GND), U44.2 (GND), U44.8 (GND), U50.2 (GND), U51.10 (VSS), U51.19 (VSSA), U51.26 (VSS), U51.49 (VSS), U51.74 (VSS), U51.99 (VSS), U52.5 (GND), U53.2 (GND), U53.8 (GND), U54.2 (GND), U54.8 (GND), U60.2 (GND), U61.10 (VSS), U61.19 (VSSA), U61.26 (VSS), U61.49 (VSS), U61.74 (VSS), U61.99 (VSS), U62.5 (GND), U63.2 (GND), U63.8 (GND), U64.2 (GND), U64.8 (GND), U70.7 (GND), U71.7 (GND), U72.7 (GND), U73.7 (GND), U74.7 (GND), U75.4 (GND), U75.5 (GND), U75.7 (GND), U75.9 (GND), U75.10 (GND), U75.12 (GND), U75.13 (GND), U76.7 (GND), U77.7 (GND), U78.7 (GND), U79.7 (GND), U79.9 (GND), U79.10 (GND), U79.12 (GND), U79.13 (GND), U80.7 (GND), U80.12 (GND), U80.13 (GND), U82.2 (GND), U83.2 (GND), U101.2 (VSS), U101.4 (VSS), U101.11 (VSS), U101.12 (VSS), U101.19 (PRSNT1), U101.20 (PRSNT2), U101.30 (VSS), U101.32 (VSS), U101.34 (VSS), U101.41 (VSS), U101.50 (VSS), U101.56 (VSS), U101.61 (VSS), U101.63 (VSS), U101.66 (VSS), U101.87 (VSS), U101.90 (VSS), U101.95 (VSS), U101.104 (VSS), U101.109 (CGND), U101.112 (CGND), U101.115 (REXT_GND), U101.120 (VSS), U101.126 (VSS), U101.129 (E_PAD), U102.49 (TEST), U102.65 (GND), U103.7 (GND), U103.9 (GND), U104.7 (GND), U104.9 (GND), U105.4 (GND), U106.4 (GND), U107.2 (GND), U109.5 (GND), U109.11 (GND), U109.20 (GND), U109.21 (EPAD), U110.5 (GND), U111.7 (GND), U111.9 (GND), U111.10 (GND), U111.12 (GND), U111.13 (GND), U201.2 (VSS), U201.4 (VSS), U201.11 (VSS), U201.12 (VSS), U201.19 (PRSNT1), U201.20 (PRSNT2), U201.30 (VSS), U201.32 (VSS), U201.34 (VSS), U201.41 (VSS), U201.50 (VSS), U201.56 (VSS), U201.61 (VSS), U201.63 (VSS), U201.66 (VSS), U201.87 (VSS), U201.90 (VSS), U201.95 (VSS), U201.104 (VSS), U201.109 (CGND), U201.112 (CGND), U201.115 (REXT_GND), U201.120 (VSS), U201.126 (VSS), U201.129 (E_PAD), U202.49 (TEST), U202.65 (GND), U203.7 (GND), U203.9 (GND), U204.7 (GND), U204.9 (GND), U205.4 (GND), U206.4 (GND), U207.2 (GND), U209.5 (GND), U209.11 (GND), U209.20 (GND), U209.21 (EPAD), U210.5 (GND), U211.7 (GND), U211.9 (GND), U211.10 (GND), U211.12 (GND), U211.13 (GND), U301.2 (VSS), U301.4 (VSS), U301.11 (VSS), U301.12 (VSS), U301.19 (PRSNT1), U301.20 (PRSNT2), U301.30 (VSS), U301.32 (VSS), U301.34 (VSS), U301.41 (VSS), U301.50 (VSS), U301.56 (VSS), U301.61 (VSS), U301.63 (VSS), U301.66 (VSS), U301.87 (VSS), U301.90 (VSS), U301.95 (VSS), U301.104 (VSS), U301.109 (CGND), U301.112 (CGND), U301.115 (REXT_GND), U301.120 (VSS), U301.126 (VSS), U301.129 (E_PAD), U302.49 (TEST), U302.65 (GND), U303.7 (GND), U303.9 (GND), U304.7 (GND), U304.9 (GND), U305.4 (GND), U306.4 (GND), U307.2 (GND), U309.5 (GND), U309.11 (GND), U309.20 (GND), U309.21 (EPAD), U310.5 (GND), U311.7 (GND), U311.9 (GND), U311.10 (GND), U311.12 (GND), U311.13 (GND), Y1.2 (G), Y1.4 (G), Y2.2 (G), Y2.4 (G), Y3.2 (G), Y3.4 (G), Y4.2 (G), Y4.4 (G), Y101.2 (G), Y101.4 (G), Y201.2 (G), Y201.4 (G), Y301.2 (G), Y301.4 (G)
GNSS_3V3: C43.1, C44.1, R24.2, U15.6 (VDD)
GNSS_ANT: C42.1, J_GNSS1.1 (In), L3.2
GNSS_BIAS: L3.1, R23.2
GNSS_DM: U15.5 (D-), U202.2 (USB_DM_DN1)
GNSS_DP: U15.4 (D+), U202.1 (USB_DP_DN1)
GNSS_PPS: Q104.3 (D), Q204.3 (D), Q304.3 (D), R22.1, TP9.1, U11.3 (1PPS)
GNSS_PPS_CM1: Q104.2 (S), R156.1, U30A.46 (GPIO22)
GNSS_PPS_CM2: Q204.2 (S), R256.1, U31A.46 (GPIO22)
GNSS_PPS_CM3: Q304.2 (S), R356.1, U32A.46 (GPIO22)
GNSS_RF_IN: C42.2, U11.11 (RF_IN)
GNSS_RST: R24.1, U15.9 (RSTb)
GNSS_RST_n: R21.1, U11.8 (RESET_N)
GNSS_RXD: U11.21 (RXD1), U15.26 (TXD)
GNSS_RXD2: J_GNSS2.3, U11.7 (RXD2)
GNSS_TXD: U11.20 (TXD1), U15.25 (RXD)
GNSS_TXD2: J_GNSS2.2, U11.6 (TXD2)
GNSS_VDD_RF: R23.1, U11.9 (VDD_RF)
HB1: J_PANEL.18, Q105.3 (D), R158.1, U41.30 (PA6), U51.30 (PA6), U61.30 (PA6)
HB2: J_PANEL.19, Q205.3 (D), R258.1, U41.31 (PA7), U51.31 (PA7), U61.31 (PA7)
HB3: J_PANEL.20, Q305.3 (D), R358.1, U41.32 (PC4), U51.32 (PC4), U61.32 (PC4)
HB_CM1: Q105.2 (S), R157.1, U30A.29 (GPIO16)
HB_CM2: Q205.2 (S), R257.1, U31A.29 (GPIO16)
HB_CM3: Q305.2 (S), R357.1, U32A.29 (GPIO16)
HDMI1_CEC: U3.18 (CEC_A), U30B.151 (HDMI0_CEC)
HDMI1_CK_N: U3.31 (D3N_A), U30B.190 (HDMI0_CLK_N)
HDMI1_CK_P: U3.32 (D3P_A), U30B.188 (HDMI0_CLK_P)
HDMI1_D0_N: U3.37 (D0N_A), U30B.184 (HDMI0_TX0_N)
HDMI1_D0_P: U3.38 (D0P_A), U30B.182 (HDMI0_TX0_P)
HDMI1_D1_N: U3.35 (D1N_A), U30B.178 (HDMI0_TX1_N)
HDMI1_D1_P: U3.36 (D1P_A), U30B.176 (HDMI0_TX1_P)
HDMI1_D2_N: U3.33 (D2N_A), U30B.172 (HDMI0_TX2_N)
HDMI1_D2_P: U3.34 (D2P_A), U30B.170 (HDMI0_TX2_P)
HDMI1_HPD: U3.19 (HPD_A), U30B.153 (HDMI0_HOTPLUG)
HDMI1_SCL: U3.42 (SCL_A), U30B.200 (HDMI0_SCL)
HDMI1_SDA: U3.41 (SDA_A), U30B.199 (HDMI0_SDA)
HDMI2_CEC: U3.20 (CEC_B), U31B.151 (HDMI0_CEC)
HDMI2_CK_N: U3.22 (D3N_B), U31B.190 (HDMI0_CLK_N)
HDMI2_CK_P: U3.23 (D3P_B), U31B.188 (HDMI0_CLK_P)
HDMI2_D0_N: U3.28 (D0N_B), U31B.184 (HDMI0_TX0_N)
HDMI2_D0_P: U3.29 (D0P_B), U31B.182 (HDMI0_TX0_P)
HDMI2_D1_N: U3.26 (D1N_B), U31B.178 (HDMI0_TX1_N)
HDMI2_D1_P: U3.27 (D1P_B), U31B.176 (HDMI0_TX1_P)
HDMI2_D2_N: U3.24 (D2N_B), U31B.172 (HDMI0_TX2_N)
HDMI2_D2_P: U3.25 (D2P_B), U31B.170 (HDMI0_TX2_P)
HDMI2_HPD: U3.21 (HPD_B), U31B.153 (HDMI0_HOTPLUG)
HDMI2_SCL: U3.40 (SCL_B), U31B.200 (HDMI0_SCL)
HDMI2_SDA: U3.39 (SDA_B), U31B.199 (HDMI0_SDA)
HDMI3_CEC: U4.20 (CEC_B), U32B.151 (HDMI0_CEC)
HDMI3_CK_N: U4.22 (D3N_B), U32B.190 (HDMI0_CLK_N)
HDMI3_CK_P: U4.23 (D3P_B), U32B.188 (HDMI0_CLK_P)
HDMI3_D0_N: U4.28 (D0N_B), U32B.184 (HDMI0_TX0_N)
HDMI3_D0_P: U4.29 (D0P_B), U32B.182 (HDMI0_TX0_P)
HDMI3_D1_N: U4.26 (D1N_B), U32B.178 (HDMI0_TX1_N)
HDMI3_D1_P: U4.27 (D1P_B), U32B.176 (HDMI0_TX1_P)
HDMI3_D2_N: U4.24 (D2N_B), U32B.172 (HDMI0_TX2_N)
HDMI3_D2_P: U4.25 (D2P_B), U32B.170 (HDMI0_TX2_P)
HDMI3_HPD: U4.21 (HPD_B), U32B.153 (HDMI0_HOTPLUG)
HDMI3_SCL: U4.40 (SCL_B), U32B.200 (HDMI0_SCL)
HDMI3_SDA: U4.39 (SDA_B), U32B.199 (HDMI0_SDA)
HDMIM_CEC: U3.15 (CEC), U4.18 (CEC_A)
HDMIM_CK_N: U3.13 (D3N), U4.31 (D3N_A)
HDMIM_CK_P: U3.12 (D3P), U4.32 (D3P_A)
HDMIM_D0_N: U3.6 (D0N), U4.37 (D0N_A)
HDMIM_D0_P: U3.5 (D0P), U4.38 (D0P_A)
HDMIM_D1_N: U3.8 (D1N), U4.35 (D1N_A)
HDMIM_D1_P: U3.7 (D1P), U4.36 (D1P_A)
HDMIM_D2_N: U3.11 (D2N), U4.33 (D2N_A)
HDMIM_D2_P: U3.10 (D2P), U4.34 (D2P_A)
HDMIM_HPD: U3.14 (HPD), U4.19 (HPD_A)
HDMIM_SCL: U3.3 (SCL), U4.42 (SCL_A)
HDMIM_SDA: U3.4 (SDA), U4.41 (SDA_A)
HDMIO_CEC: J_HDMI.13 (CEC), U4.15 (CEC)
HDMIO_CK_N: J_HDMI.12 (CK-), U4.13 (D3N)
HDMIO_CK_P: J_HDMI.10 (CK+), U4.12 (D3P)
HDMIO_D0_N: J_HDMI.9 (D0-), U4.6 (D0N)
HDMIO_D0_P: J_HDMI.7 (D0+), U4.5 (D0P)
HDMIO_D1_N: J_HDMI.6 (D1-), U4.8 (D1N)
HDMIO_D1_P: J_HDMI.4 (D1+), U4.7 (D1P)
HDMIO_D2_N: J_HDMI.3 (D2-), U4.11 (D2N)
HDMIO_D2_P: J_HDMI.1 (D2+), U4.10 (D2P)
HDMIO_HPD: R19.2, R20.1, U4.14 (HPD)
HDMIO_HPD_IN: J_HDMI.19 (HPD), R19.1
HDMIO_SCL: J_HDMI.15 (SCL), R17.1, U4.3 (SCL)
HDMIO_SDA: J_HDMI.16 (SDA), R18.1, U4.4 (SDA)
HDMI_SEL1: J_PANEL.12, R15.1, TP18.1, U3.17 (SEL2)
HDMI_SEL2: J_PANEL.13, R16.1, TP19.1, U4.17 (SEL2)
HDMI_SW_EN: R14.1, U3.2 (EN), U3.16 (SEL1), U4.2 (EN), U4.16 (SEL1)
HOST1_0D_N: U30B.136 (USB3-0-DM), U110.2 (1Dn)
HOST1_0D_P: U30B.134 (USB3-0-DP), U110.1 (1Dp)
HOST1_0RX_N: U30B.128 (USB3-0-RX_N), U109.16 (B1n)
HOST1_0RX_P: U30B.130 (USB3-0-RX_P), U109.17 (B1p)
HOST1_0TX_N: U30B.140 (USB3-0-TX_N), U109.18 (B0n)
HOST1_0TX_P: U30B.142 (USB3-0-TX_P), U109.19 (B0p)
HOST1_1D_N: U30B.165 (USB3-1-DM), U310.4 (2Dn)
HOST1_1D_P: U30B.163 (USB3-1-DP), U310.3 (2Dp)
HOST1_1RX_N: U30B.157 (USB3-1-RX_N), U309.12 (C1n)
HOST1_1RX_P: U30B.159 (USB3-1-RX_P), U309.13 (C1p)
HOST1_1TX_N: U30B.169 (USB3-1-TX_N), U309.14 (C0n)
HOST1_1TX_P: U30B.171 (USB3-1-TX_P), U309.15 (C0p)
HOST2_0D_N: U31B.136 (USB3-0-DM), U210.2 (1Dn)
HOST2_0D_P: U31B.134 (USB3-0-DP), U210.1 (1Dp)
HOST2_0RX_N: U31B.128 (USB3-0-RX_N), U209.16 (B1n)
HOST2_0RX_P: U31B.130 (USB3-0-RX_P), U209.17 (B1p)
HOST2_0TX_N: U31B.140 (USB3-0-TX_N), U209.18 (B0n)
HOST2_0TX_P: U31B.142 (USB3-0-TX_P), U209.19 (B0p)
HOST2_1D_N: U31B.165 (USB3-1-DM), U110.4 (2Dn)
HOST2_1D_P: U31B.163 (USB3-1-DP), U110.3 (2Dp)
HOST2_1RX_N: U31B.157 (USB3-1-RX_N), U109.12 (C1n)
HOST2_1RX_P: U31B.159 (USB3-1-RX_P), U109.13 (C1p)
HOST2_1TX_N: U31B.169 (USB3-1-TX_N), U109.14 (C0n)
HOST2_1TX_P: U31B.171 (USB3-1-TX_P), U109.15 (C0p)
HOST3_0D_N: U32B.136 (USB3-0-DM), U310.2 (1Dn)
HOST3_0D_P: U32B.134 (USB3-0-DP), U310.1 (1Dp)
HOST3_0RX_N: U32B.128 (USB3-0-RX_N), U309.16 (B1n)
HOST3_0RX_P: U32B.130 (USB3-0-RX_P), U309.17 (B1p)
HOST3_0TX_N: U32B.140 (USB3-0-TX_N), U309.18 (B0n)
HOST3_0TX_P: U32B.142 (USB3-0-TX_P), U309.19 (B0p)
HOST3_1D_N: U32B.165 (USB3-1-DM), U210.4 (2Dn)
HOST3_1D_P: U32B.163 (USB3-1-DP), U210.3 (2Dp)
HOST3_1RX_N: U32B.157 (USB3-1-RX_N), U209.12 (C1n)
HOST3_1RX_P: U32B.159 (USB3-1-RX_P), U209.13 (C1p)
HOST3_1TX_N: U32B.169 (USB3-1-TX_N), U209.14 (C0n)
HOST3_1TX_P: U32B.171 (USB3-1-TX_P), U209.15 (C0p)
HUB1_D1TX_N: C162.1, U102.4 (USB_SSTXM_DN1)
HUB1_D1TX_P: C161.1, U102.3 (USB_SSTXP_DN1)
HUB1_PWRPOL: R146.1, U102.41 (PWRCTL_POL)
HUB1_R1: R142.1, U102.64 (USB_R1)
HUB1_RST_n: C163.1, Q3.3 (D), R141.1, U102.50 (GRSTz)
HUB1_SMBUS_n: R145.1, U102.39 (SMBUSz)
HUB1_VBUS: R143.2, R144.1, U102.48 (USB_VBUS)
HUB1_XI: C164.1, R147.1, U102.62 (XI), Y101.1
HUB1_XO: C165.1, R147.2, U102.61 (XO), Y101.3
HUB2_PWRPOL: R246.1, U202.41 (PWRCTL_POL)
HUB2_R1: R242.1, U202.64 (USB_R1)
HUB2_RST_n: C263.1, Q4.3 (D), R241.1, U202.50 (GRSTz)
HUB2_SMBUS_n: R245.1, U202.39 (SMBUSz)
HUB2_VBUS: R243.2, R244.1, U202.48 (USB_VBUS)
HUB2_XI: C264.1, R247.1, U202.62 (XI), Y201.1
HUB2_XO: C265.1, R247.2, U202.61 (XO), Y201.3
HUB3_PWRPOL: R346.1, U302.41 (PWRCTL_POL)
HUB3_R1: R342.1, U302.64 (USB_R1)
HUB3_RST_n: C363.1, Q5.3 (D), R341.1, U302.50 (GRSTz)
HUB3_SMBUS_n: R345.1, U302.39 (SMBUSz)
HUB3_VBUS: R343.2, R344.1, U302.48 (USB_VBUS)
HUB3_XI: C364.1, R347.1, U302.62 (XI), Y301.1
HUB3_XO: C365.1, R347.2, U302.61 (XO), Y301.3
HUBRST1_A: R489.1, TP523.1, U41.25 (PA3), U72.4 (HUBRST1_A), U72.12 (HUBRST1_A)
HUBRST1_AB: U72.6 (HUBRST1_AB), U77.10 (HUBRST1_AB)
HUBRST1_B: R490.1, TP524.1, U51.25 (PA3), U72.5 (HUBRST1_B), U72.10 (HUBRST1_B)
HUBRST1_BC: U72.8 (HUBRST1_BC), U77.9 (HUBRST1_BC)
HUBRST1_C: R491.1, TP525.1, U61.25 (PA3), U72.9 (HUBRST1_C), U72.13 (HUBRST1_C)
HUBRST1_CA: U72.11 (HUBRST1_CA), U77.12 (HUBRST1_CA)
HUBRST1_O1: U77.8 (HUBRST1_O1), U77.13 (HUBRST1_O1)
HUBRST1_VOTE: Q3.1 (G), R477.1, TP511.1, U77.11 (HUBRST1_VOTE)
HUBRST2_A: R492.1, TP526.1, U41.28 (PA4), U73.1 (HUBRST2_A), U73.9 (HUBRST2_A)
HUBRST2_AB: U73.3 (HUBRST2_AB), U78.1 (HUBRST2_AB)
HUBRST2_B: R493.1, TP527.1, U51.28 (PA4), U73.2 (HUBRST2_B), U73.4 (HUBRST2_B)
HUBRST2_BC: U73.6 (HUBRST2_BC), U78.2 (HUBRST2_BC)
HUBRST2_C: R494.1, TP528.1, U61.28 (PA4), U73.5 (HUBRST2_C), U73.10 (HUBRST2_C)
HUBRST2_CA: U73.8 (HUBRST2_CA), U78.5 (HUBRST2_CA)
HUBRST2_O1: U78.3 (HUBRST2_O1), U78.4 (HUBRST2_O1)
HUBRST2_VOTE: Q4.1 (G), R478.1, TP512.1, U78.6 (HUBRST2_VOTE)
HUBRST3_A: R495.1, TP529.1, U41.29 (PA5), U73.13 (HUBRST3_A), U74.5 (HUBRST3_A)
HUBRST3_AB: U73.11 (HUBRST3_AB), U78.10 (HUBRST3_AB)
HUBRST3_B: R496.1, TP530.1, U51.29 (PA5), U73.12 (HUBRST3_B), U74.1 (HUBRST3_B)
HUBRST3_BC: U74.3 (HUBRST3_BC), U78.9 (HUBRST3_BC)
HUBRST3_C: R497.1, TP531.1, U61.29 (PA5), U74.2 (HUBRST3_C), U74.4 (HUBRST3_C)
HUBRST3_CA: U74.6 (HUBRST3_CA), U78.12 (HUBRST3_CA)
HUBRST3_O1: U78.8 (HUBRST3_O1), U78.13 (HUBRST3_O1)
HUBRST3_VOTE: Q5.1 (G), R479.1, TP513.1, U78.11 (HUBRST3_VOTE)
IOCA_BOOT0: R64.1, U41.94 (BOOT0)
IOCA_CAN1_RX: U41.81 (PD0), U43.4 (IOCA_CAN1_RX)
IOCA_CAN1_TX: U41.82 (PD1), U43.1 (IOCA_CAN1_TX)
IOCA_CAN2_RX: U41.51 (PB12), U44.4 (IOCA_CAN2_RX)
IOCA_CAN2_TX: U41.52 (PB13), U44.1 (IOCA_CAN2_TX)
IOCA_LDO_EN: J_IOCOFF_A.1, R66.2, U40.3 (IOCA_LDO_EN)
IOCA_LED_A: LED40.2 (A), U41.34 (PB0)
IOCA_LED_K: LED40.1 (K), R65.2
IOCA_RST_n: C409.1, R63.1, U41.14 (NRST), U42.4 (IOCA_RST_n)
IOCA_SWCLK: U41.76 (PA14), U42.3 (IOCA_SWCLK)
IOCA_SWDIO: U41.72 (PA13), U42.2 (IOCA_SWDIO)
IOCA_VCAP: C407.1, C408.1, U41.48 (VCAP), U41.73 (VCAP)
IOCA_XI: C410.1, U41.12 (PH0), Y2.1
IOCA_XO: C411.1, U41.13 (PH1), Y2.3
IOCB_BOOT0: R76.1, U51.94 (BOOT0)
IOCB_CAN1_RX: U51.81 (PD0), U53.4 (IOCB_CAN1_RX)
IOCB_CAN1_TX: U51.82 (PD1), U53.1 (IOCB_CAN1_TX)
IOCB_CAN2_RX: U51.51 (PB12), U54.4 (IOCB_CAN2_RX)
IOCB_CAN2_TX: U51.52 (PB13), U54.1 (IOCB_CAN2_TX)
IOCB_LDO_EN: J_IOCOFF_B.1, R78.2, U50.3 (IOCB_LDO_EN)
IOCB_LED_A: LED41.2 (A), U51.34 (PB0)
IOCB_LED_K: LED41.1 (K), R77.2
IOCB_RST_n: C429.1, R75.1, U51.14 (NRST), U52.4 (IOCB_RST_n)
IOCB_SWCLK: U51.76 (PA14), U52.3 (IOCB_SWCLK)
IOCB_SWDIO: U51.72 (PA13), U52.2 (IOCB_SWDIO)
IOCB_VCAP: C427.1, C428.1, U51.48 (VCAP), U51.73 (VCAP)
IOCB_XI: C430.1, U51.12 (PH0), Y3.1
IOCB_XO: C431.1, U51.13 (PH1), Y3.3
IOCC_BOOT0: R88.1, U61.94 (BOOT0)
IOCC_CAN1_RX: U61.81 (PD0), U63.4 (IOCC_CAN1_RX)
IOCC_CAN1_TX: U61.82 (PD1), U63.1 (IOCC_CAN1_TX)
IOCC_CAN2_RX: U61.51 (PB12), U64.4 (IOCC_CAN2_RX)
IOCC_CAN2_TX: U61.52 (PB13), U64.1 (IOCC_CAN2_TX)
IOCC_LDO_EN: J_IOCOFF_C.1, R90.2, U60.3 (IOCC_LDO_EN)
IOCC_LED_A: LED42.2 (A), U61.34 (PB0)
IOCC_LED_K: LED42.1 (K), R89.2
IOCC_RST_n: C449.1, R87.1, U61.14 (NRST), U62.4 (IOCC_RST_n)
IOCC_SWCLK: U61.76 (PA14), U62.3 (IOCC_SWCLK)
IOCC_SWDIO: U61.72 (PA13), U62.2 (IOCC_SWDIO)
IOCC_VCAP: C447.1, C448.1, U61.48 (VCAP), U61.73 (VCAP)
IOCC_XI: C450.1, U61.12 (PH0), Y4.1
IOCC_XO: C451.1, U61.13 (PH1), Y4.3
KSZC_BST: C10.1, U26.6 (KSZC_BST)
KSZC_FB: R1.2, R2.1, U26.8 (KSZC_FB)
KSZC_SS: C11.1, U26.7 (KSZC_SS)
KSZC_SW: C10.2, L2.1, U26.5 (KSZC_SW)
KSZ_ISET: R3.1, U1.127 (ISET)
KSZ_LED1: LED1.1 (K), U1.105 (LED1_0)
KSZ_LED2: LED2.1 (K), U1.91 (LED2_0)
KSZ_LED3: LED3.1 (K), U1.88 (LED3_0)
KSZ_LED4: LED4.1 (K), U1.85 (LED4_0)
KSZ_RST: Q2.1 (G), R60.1, U6.4 (IO0_0)
KSZ_RST_n: C16.1, Q2.3 (D), R4.1, U1.96 (RESET_N)
KSZ_STRAP_I2C: R57.1, U1.86 (LED4_1)
KSZ_XI: C14.1, U1.126 (XI), Y1.1
KSZ_XO: C15.1, U1.125 (XO), Y1.3
LED_5G_A: LED25.2 (A), R239.2
LED_5V_A1: LED11.2 (A), R101.2
LED_5V_A2: LED21.2 (A), R201.2
LED_5V_A3: LED31.2 (A), R301.2
LED_ACT_A1: LED16.2 (A), R148.2
LED_ACT_A2: LED26.2 (A), R248.2
LED_ACT_A3: LED36.2 (A), R348.2
LED_KSZ_A1: LED1.2 (A), R5.2
LED_KSZ_A2: LED2.2 (A), R6.2
LED_KSZ_A3: LED3.2 (A), R7.2
LED_KSZ_A4: LED4.2 (A), R8.2
LED_NV_A1: LED14.2 (A), R136.2
LED_NV_A2: LED24.2 (A), R236.2
LED_NV_A3: LED34.2 (A), R336.2
LED_PST0_A1: LED12.2 (A), R130.2
LED_PST0_A2: LED22.2 (A), R230.2
LED_PST0_A3: LED32.2 (A), R330.2
LED_PST1_A1: LED13.2 (A), R131.2
LED_PST1_A2: LED23.2 (A), R231.2
LED_PST1_A3: LED33.2 (A), R331.2
LED_PWR_A1: LED17.2 (A), R150.2
LED_PWR_A2: LED27.2 (A), R250.2
LED_PWR_A3: LED37.2 (A), R350.2
LED_WIFI2_A: LED35.2 (A), R339.2
LED_WIFI_A: LED15.2 (A), R139.2
LED_ZBAG_A: LED7.2 (A), R34.2
LED_ZBAR_A: LED6.2 (A), R32.2
LED_ZBBG_A: LED9.2 (A), R35.2
LED_ZBBR_A: LED8.2 (A), R33.2
LED_nACT1: LED16.1 (K), U30A.21 (LED_nACT)
LED_nACT2: LED26.1 (K), U31A.21 (LED_nACT)
LED_nACT3: LED36.1 (K), U32A.21 (LED_nACT)
LED_nPWR1: R149.1, U30A.95 (LED_nPWR)
LED_nPWR2: R249.1, U31A.95 (LED_nPWR)
LED_nPWR3: R349.1, U32A.95 (LED_nPWR)
LIME_DM: J_LIME.2 (D-), U33.3 (I/O2), U33.4 (I/O2), U102.2 (USB_DM_DN1)
LIME_DP: J_LIME.3 (D+), U33.1 (I/O1), U33.6 (I/O1), U102.1 (USB_DP_DN1)
LIME_EN: R514.1, U19.6 (LIME_EN), U23.3 (LIME_EN)
LIME_EN_A: U19.3 (LIME_EN_A), U19.4 (LIME_EN_A)
LIME_FLT: R37.1, U7.4 (IO0_0), U23.6 (LIME_FLT), U102.46 (OVERCUR1z)
LIME_HW_EN: R49.1, U19.2 (LIME_HW_EN), U102.36 (PWRCTL1)
LIME_SSRX_N: J_LIME.5 (SSRX-), U102.7 (USB_SSRXM_DN1)
LIME_SSRX_P: J_LIME.6 (SSRX+), U102.6 (USB_SSRXP_DN1)
LIME_SSTX_N: C162.2, J_LIME.8 (SSTX-)
LIME_SSTX_P: C161.2, J_LIME.9 (SSTX+)
LIME_SW_EN: R50.1, U6.5 (IO0_1), U19.5 (LIME_SW_EN)
LORA_ANT: J_LORA1.1 (In), U12.21 (ANT)
LORA_ON: R52.1, U6.7 (IO0_3), U19.13 (LORA_ON)
LORA_RXEN: U12.6 (RXEN), U32A.34 (GPIO5)
LORA_TXEN: U12.7 (TXEN), U32A.54 (GPIO4)
MCT3: R9.1, T1.18 (MCT3)
MCT4: R10.1, T1.15 (MCT4)
MDI_A_N: J_ETH.2, T1.22 (MX1N)
MDI_A_P: J_ETH.1, T1.23 (MX1P)
MDI_B_N: J_ETH.6, T1.19 (MX2N)
MDI_B_P: J_ETH.3, T1.20 (MX2P)
MDI_C_N: J_ETH.5, T1.16 (MX3N)
MDI_C_P: J_ETH.4, T1.17 (MX3P)
MDI_D_N: J_ETH.8, T1.13 (MX4N)
MDI_D_P: J_ETH.7, T1.14 (MX4P)
MUX1_A1N: C160.2, U109.8 (A1n)
MUX1_A1P: C159.2, U109.7 (A1p)
MUX2_A1N: C260.2, U209.8 (A1n)
MUX2_A1P: C259.2, U209.7 (A1p)
MUX3_A1N: C360.2, U309.8 (A1n)
MUX3_A1P: C359.2, U309.7 (A1p)
NVME1_CLKREQ_n: J_M2N1.52 (~CLKREQ), R133.1
NVME1_CLK_N: J_M2N1.53 (REFCLKn), R180.2, R182.1
NVME1_CLK_P: J_M2N1.55 (REFCLKp), R179.2, R181.1
NVME1_CLK_SRC_N: R180.1, U101.80 (REFCLKO_N1)
NVME1_CLK_SRC_P: R179.1, U101.81 (REFCLKO_P1)
NVME1_DEVSLP: J_M2N1.38 (DEVSLP), R135.1
NVME1_RX_N: C154.2, J_M2N1.47 (PETn0/SATA-A-)
NVME1_RX_P: C153.2, J_M2N1.49 (PETp0/SATA-A+)
NVME1_RX_SW_N: C154.1, U101.101 (PETN1)
NVME1_RX_SW_P: C153.1, U101.100 (PETP1)
NVME1_TX_N: J_M2N1.41 (PERn0/SATA-B+), U101.98 (PERN1)
NVME1_TX_P: J_M2N1.43 (PERp0/SATA-B-), U101.97 (PERP1)
NVME1_nLED: J_M2N1.10 (DAS/~DSS/~LED1), LED14.1 (K)
NVME2_CLKREQ_n: J_M2N2.52 (~CLKREQ), R233.1
NVME2_CLK_N: J_M2N2.53 (REFCLKn), R280.2, R282.1
NVME2_CLK_P: J_M2N2.55 (REFCLKp), R279.2, R281.1
NVME2_CLK_SRC_N: R280.1, U201.80 (REFCLKO_N1)
NVME2_CLK_SRC_P: R279.1, U201.81 (REFCLKO_P1)
NVME2_DEVSLP: J_M2N2.38 (DEVSLP), R235.1
NVME2_RX_N: C254.2, J_M2N2.47 (PETn0/SATA-A-)
NVME2_RX_P: C253.2, J_M2N2.49 (PETp0/SATA-A+)
NVME2_RX_SW_N: C254.1, U201.101 (PETN1)
NVME2_RX_SW_P: C253.1, U201.100 (PETP1)
NVME2_TX_N: J_M2N2.41 (PERn0/SATA-B+), U201.98 (PERN1)
NVME2_TX_P: J_M2N2.43 (PERp0/SATA-B-), U201.97 (PERP1)
NVME2_nLED: J_M2N2.10 (DAS/~DSS/~LED1), LED24.1 (K)
NVME3_CLKREQ_n: J_M2N3.52 (~CLKREQ), R333.1
NVME3_CLK_N: J_M2N3.53 (REFCLKn), R380.2, R382.1
NVME3_CLK_P: J_M2N3.55 (REFCLKp), R379.2, R381.1
NVME3_CLK_SRC_N: R380.1, U301.80 (REFCLKO_N1)
NVME3_CLK_SRC_P: R379.1, U301.81 (REFCLKO_P1)
NVME3_DEVSLP: J_M2N3.38 (DEVSLP), R335.1
NVME3_RX_N: C354.2, J_M2N3.47 (PETn0/SATA-A-)
NVME3_RX_P: C353.2, J_M2N3.49 (PETp0/SATA-A+)
NVME3_RX_SW_N: C354.1, U301.101 (PETN1)
NVME3_RX_SW_P: C353.1, U301.100 (PETP1)
NVME3_TX_N: J_M2N3.41 (PERn0/SATA-B+), U301.98 (PERN1)
NVME3_TX_P: J_M2N3.43 (PERp0/SATA-B-), U301.97 (PERP1)
NVME3_nLED: J_M2N3.10 (DAS/~DSS/~LED1), LED34.1 (K)
PANEL_5V: F1.2, J_PANEL.1, J_PANEL.2
PCIE1_CLKREQ_n: R129.1, U30B.102 (PCIe_CLK_nREQ)
PCIE1_CLK_N: U30B.112 (PCIe_CLK_N), U101.73 (REFCLKI_N)
PCIE1_CLK_P: U30B.110 (PCIe_CLK_P), U101.74 (REFCLKI_P)
PCIE1_RCLK0_N: C196.1, R176.2, R178.1
PCIE1_RCLK0_P: C195.1, R175.2, R177.1
PCIE1_RCLK0_SRC_N: R176.1, U101.83 (REFCLKO_N0)
PCIE1_RCLK0_SRC_P: R175.1, U101.85 (REFCLKO_P0)
PCIE1_RCLKIN_N: C196.2, U101.111 (REFCLKN)
PCIE1_RCLKIN_P: C195.2, U101.110 (REFCLKP)
PCIE1_RST1_n: J_M2N1.50 (~PERST), U101.5 (DWNRST_L1)
PCIE1_RST2_n: J_M2C1.52 (~PERST0), U101.6 (DWNRST_L2)
PCIE1_RXSW_N: C152.1, U101.123 (PETN0)
PCIE1_RXSW_P: C151.1, U101.124 (PETP0)
PCIE1_RX_N: C152.2, U30B.118 (PCIe_RX_N)
PCIE1_RX_P: C151.2, U30B.116 (PCIe_RX_P)
PCIE1_TX_N: U30B.124 (PCIe_TX_N), U101.127 (PERN0)
PCIE1_TX_P: U30B.122 (PCIe_TX_P), U101.128 (PERP0)
PCIE1_nRST: U30B.109 (PCIe_nRST), U101.10 (PERST_L)
PCIE1_nWAKE: J_M2C1.55 (~PEWAKE0), J_M2N1.54 (~PEWAKE), R132.1, U30B.104 (PCIE_nWAKE)
PCIE2_CLKREQ_n: R229.1, U31B.102 (PCIe_CLK_nREQ)
PCIE2_CLK_N: U31B.112 (PCIe_CLK_N), U201.73 (REFCLKI_N)
PCIE2_CLK_P: U31B.110 (PCIe_CLK_P), U201.74 (REFCLKI_P)
PCIE2_RCLK0_N: C296.1, R276.2, R278.1
PCIE2_RCLK0_P: C295.1, R275.2, R277.1
PCIE2_RCLK0_SRC_N: R276.1, U201.83 (REFCLKO_N0)
PCIE2_RCLK0_SRC_P: R275.1, U201.85 (REFCLKO_P0)
PCIE2_RCLKIN_N: C296.2, U201.111 (REFCLKN)
PCIE2_RCLKIN_P: C295.2, U201.110 (REFCLKP)
PCIE2_RST1_n: J_M2N2.50 (~PERST), U201.5 (DWNRST_L1)
PCIE2_RST2_n: J_M2C2.50 (~PERST), U201.6 (DWNRST_L2)
PCIE2_RXSW_N: C252.1, U201.123 (PETN0)
PCIE2_RXSW_P: C251.1, U201.124 (PETP0)
PCIE2_RX_N: C252.2, U31B.118 (PCIe_RX_N)
PCIE2_RX_P: C251.2, U31B.116 (PCIe_RX_P)
PCIE2_TX_N: U31B.124 (PCIe_TX_N), U201.127 (PERN0)
PCIE2_TX_P: U31B.122 (PCIe_TX_P), U201.128 (PERP0)
PCIE2_nRST: U31B.109 (PCIe_nRST), U201.10 (PERST_L)
PCIE2_nWAKE: J_M2C2.54 (~PEWAKE), J_M2N2.54 (~PEWAKE), R232.1, U31B.104 (PCIE_nWAKE)
PCIE3_CLKREQ_n: R329.1, U32B.102 (PCIe_CLK_nREQ)
PCIE3_CLK_N: U32B.112 (PCIe_CLK_N), U301.73 (REFCLKI_N)
PCIE3_CLK_P: U32B.110 (PCIe_CLK_P), U301.74 (REFCLKI_P)
PCIE3_RCLK0_N: C396.1, R376.2, R378.1
PCIE3_RCLK0_P: C395.1, R375.2, R377.1
PCIE3_RCLK0_SRC_N: R376.1, U301.83 (REFCLKO_N0)
PCIE3_RCLK0_SRC_P: R375.1, U301.85 (REFCLKO_P0)
PCIE3_RCLKIN_N: C396.2, U301.111 (REFCLKN)
PCIE3_RCLKIN_P: C395.2, U301.110 (REFCLKP)
PCIE3_RST1_n: J_M2N3.50 (~PERST), U301.5 (DWNRST_L1)
PCIE3_RST2_n: J_M2C3.52 (~PERST0), U301.6 (DWNRST_L2)
PCIE3_RXSW_N: C352.1, U301.123 (PETN0)
PCIE3_RXSW_P: C351.1, U301.124 (PETP0)
PCIE3_RX_N: C352.2, U32B.118 (PCIe_RX_N)
PCIE3_RX_P: C351.2, U32B.116 (PCIe_RX_P)
PCIE3_TX_N: U32B.124 (PCIe_TX_N), U301.127 (PERN0)
PCIE3_TX_P: U32B.122 (PCIe_TX_P), U301.128 (PERP0)
PCIE3_nRST: U32B.109 (PCIe_nRST), U301.10 (PERST_L)
PCIE3_nWAKE: J_M2C3.55 (~PEWAKE0), J_M2N3.54 (~PEWAKE), R332.1, U32B.104 (PCIE_nWAKE)
PCIE_PWR_EN1: R106.1, R164.1, U30B.106 (PCIE_PWR_EN)
PCIE_PWR_EN2: R206.1, U31B.106 (PCIE_PWR_EN), U203.3 (PCIE_PWR_EN2)
PCIE_PWR_EN3: R306.1, R364.1, U32B.106 (PCIE_PWR_EN)
PI_KILL: J_AB1.10, J_PANEL.25, Q103.3 (D), Q203.3 (D), Q303.3 (D)
PI_KILL_CM1: Q103.2 (S), R155.1, U30A.50 (GPIO17)
PI_KILL_CM2: Q203.2 (S), R255.1, U31A.50 (GPIO17)
PI_KILL_CM3: Q303.2 (S), R355.1, U32A.50 (GPIO17)
PI_SHDN_REQ: J_AB1.9, J_PANEL.24, Q102.3 (D), Q202.3 (D), Q302.3 (D)
PI_SHDN_REQ_CM1: Q102.2 (S), R154.1, U30A.30 (GPIO6)
PI_SHDN_REQ_CM2: Q202.2 (S), R254.1, U31A.30 (GPIO6)
PI_SHDN_REQ_CM3: Q302.2 (S), R354.1, U32A.30 (GPIO6)
POE_DRAIN: Q1.5 (POE_DRAIN), T1.21 (MCT2), TP13.1, U5.16 (DRAIN1)
POE_GATE: Q1.4 (POE_GATE), U5.17 (GATE1)
POE_P: R13.2, T1.24 (MCT1)
POE_RST_n: R11.1, U5.2 (RESET)
POE_SEN: Q1.1 (POE_SEN), Q1.2 (POE_SEN), Q1.3 (POE_SEN), R12.1, U5.15 (SEN1)
Q1B: Q101.1 (B), R149.2
Q1C: Q101.3 (C), R150.1
Q2B: Q201.1 (B), R249.2
Q2C: Q201.3 (C), R250.1
Q3B: Q301.1 (B), R349.2
Q3C: Q301.3 (C), R350.1
QMX_DM: J_QMX.2, U35.3 (I/O2), U35.4 (I/O2), U202.25 (USB_DM_DN4)
QMX_DP: J_QMX.3, U35.1 (I/O1), U35.6 (I/O1), U202.24 (USB_DP_DN4)
RB_3V3: C59.1, C60.1, R40.2, U18.6 (VDD)
RB_CTRL: J_RB9704.6, U6.20 (IO1_7)
RB_DM: U18.5 (D-), U102.25 (USB_DM_DN4)
RB_DP: U18.4 (D+), U102.24 (USB_DP_DN4)
RB_EN: R515.1, U19.8 (RB_EN), U24.3 (RB_EN)
RB_FLT: R44.1, U7.5 (IO0_1), U24.6 (RB_FLT)
RB_IEN: J_RB9704.3, U6.19 (IO1_6)
RB_RST: R40.1, U18.9 (RSTb)
RB_RXD: J_RB9704.14, U18.26 (TXD)
RB_STATUS: J_RB9704.7, R41.1, U7.7 (IO0_3)
RB_SW_EN: R51.1, U6.6 (IO0_2), U19.10 (RB_SW_EN)
RB_TXD: J_RB9704.13, U18.25 (RXD)
RB_XMTG: J_RB9704.8, R42.1, U7.8 (IO0_4)
S1A_BOOT: C111.1, U103.1 (S1A_BOOT)
S1A_COMP: R105.1, U103.6 (S1A_COMP)
S1A_COMPC: C117.1, R105.2
S1A_EN: Q111.3 (D), R164.2, U103.3 (S1A_EN)
S1A_FB: R102.2, R103.1, U103.5 (S1A_FB)
S1A_RT: R104.1, U103.4 (S1A_RT)
S1A_SW: C111.2, L101.1, U103.8 (S1A_SW)
S1B_BOOT: C118.1, U104.1 (S1B_BOOT)
S1B_COMP: R110.1, U104.6 (S1B_COMP)
S1B_COMPC: C124.1, R110.2
S1B_FB: R107.2, R108.1, U104.5 (S1B_FB)
S1B_RT: R109.1, U104.4 (S1B_RT)
S1B_SW: C118.2, L102.1, U104.8 (S1B_SW)
S1C_BST: C128.1, U105.6 (S1C_BST)
S1C_FB: R113.2, R114.1, U105.8 (S1C_FB)
S1C_SS: C129.1, U105.7 (S1C_SS)
S1C_SW: C128.2, L103.1, U105.5 (S1C_SW)
S1D_BST: C133.1, U106.6 (S1D_BST)
S1D_FB: R115.2, R116.1, U106.8 (S1D_FB)
S1D_SS: C134.1, U106.7 (S1D_SS)
S1D_SW: C133.2, L104.1, U106.5 (S1D_SW)
S1_EEPD: R127.1, U101.71 (EEPD)
S1_IREF: R117.1, U101.86 (IREF)
S1_JTAGL: R128.1, U101.89 (TCK), U101.92 (TMS), U101.93 (TDI), U101.94 (TRST_L)
S1_PRSNT3: R121.1, U101.21 (PRSNT3)
S1_PST0: LED12.1 (K), U101.67 (PORTSTATUS0)
S1_PST1: LED13.1 (K), U101.68 (PORTSTATUS1)
S1_PWRSAV: R122.1, U101.28 (PWR_SAV)
S1_REXT: R118.1, U101.116 (REXT)
S1_SLOTCLK: R119.1, U101.33 (SLOTCLK)
S1_SLOTIMP: R120.1, U101.45 (SLOT_IMP1), U101.46 (SLOT_IMP2)
S1_SMBCLK: R125.1, U101.26 (SMBCLK)
S1_SMBDAT: R126.1, U101.27 (SMBDATA)
S1_TEST1: R123.1, U101.9 (TEST1)
S1_TESTL: R124.1, U101.16 (TEST2), U101.17 (TEST3), U101.18 (VC1_EN), U101.22 (TEST4), U101.25 (TEST5), U101.51 (TEST6)
S2A_BOOT: C211.1, U203.1 (S2A_BOOT)
S2A_COMP: C298.1, R205.1, U203.6 (S2A_COMP)
S2A_COMPC: C217.1, R205.2
S2A_FB: R202.2, R203.1, U203.5 (S2A_FB)
S2A_RT: R204.1, U203.4 (S2A_RT)
S2A_SW: C211.2, L201.1, U203.8 (S2A_SW)
S2B_BOOT: C218.1, U204.1 (S2B_BOOT)
S2B_COMP: R210.1, U204.6 (S2B_COMP)
S2B_COMPC: C224.1, R210.2
S2B_FB: R207.2, R208.1, U204.5 (S2B_FB)
S2B_RT: R209.1, U204.4 (S2B_RT)
S2B_SW: C218.2, L202.1, U204.8 (S2B_SW)
S2C_BST: C228.1, U205.6 (S2C_BST)
S2C_FB: R213.2, R214.1, U205.8 (S2C_FB)
S2C_SS: C229.1, U205.7 (S2C_SS)
S2C_SW: C228.2, L203.1, U205.5 (S2C_SW)
S2D_BST: C233.1, U206.6 (S2D_BST)
S2D_FB: R215.2, R216.1, U206.8 (S2D_FB)
S2D_SS: C234.1, U206.7 (S2D_SS)
S2D_SW: C233.2, L204.1, U206.5 (S2D_SW)
S2_EEPD: R227.1, U201.71 (EEPD)
S2_IREF: R217.1, U201.86 (IREF)
S2_JTAGL: R228.1, U201.89 (TCK), U201.92 (TMS), U201.93 (TDI), U201.94 (TRST_L)
S2_PRSNT3: R221.1, U201.21 (PRSNT3)
S2_PST0: LED22.1 (K), U201.67 (PORTSTATUS0)
S2_PST1: LED23.1 (K), U201.68 (PORTSTATUS1)
S2_PWRSAV: R222.1, U201.28 (PWR_SAV)
S2_REXT: R218.1, U201.116 (REXT)
S2_SLOTCLK: R219.1, U201.33 (SLOTCLK)
S2_SLOTIMP: R220.1, U201.45 (SLOT_IMP1), U201.46 (SLOT_IMP2)
S2_SMBCLK: R225.1, U201.26 (SMBCLK)
S2_SMBDAT: R226.1, U201.27 (SMBDATA)
S2_TEST1: R223.1, U201.9 (TEST1)
S2_TESTL: R224.1, U201.16 (TEST2), U201.17 (TEST3), U201.18 (VC1_EN), U201.22 (TEST4), U201.25 (TEST5), U201.51 (TEST6)
S3A_BOOT: C311.1, U303.1 (S3A_BOOT)
S3A_COMP: R305.1, U303.6 (S3A_COMP)
S3A_COMPC: C317.1, R305.2
S3A_EN: Q311.3 (D), R364.2, U303.3 (S3A_EN)
S3A_FB: R302.2, R303.1, U303.5 (S3A_FB)
S3A_RT: R304.1, U303.4 (S3A_RT)
S3A_SW: C311.2, L301.1, U303.8 (S3A_SW)
S3B_BOOT: C318.1, U304.1 (S3B_BOOT)
S3B_COMP: R310.1, U304.6 (S3B_COMP)
S3B_COMPC: C324.1, R310.2
S3B_FB: R307.2, R308.1, U304.5 (S3B_FB)
S3B_RT: R309.1, U304.4 (S3B_RT)
S3B_SW: C318.2, L302.1, U304.8 (S3B_SW)
S3C_BST: C328.1, U305.6 (S3C_BST)
S3C_FB: R313.2, R314.1, U305.8 (S3C_FB)
S3C_SS: C329.1, U305.7 (S3C_SS)
S3C_SW: C328.2, L303.1, U305.5 (S3C_SW)
S3D_BST: C333.1, U306.6 (S3D_BST)
S3D_FB: R315.2, R316.1, U306.8 (S3D_FB)
S3D_SS: C334.1, U306.7 (S3D_SS)
S3D_SW: C333.2, L304.1, U306.5 (S3D_SW)
S3_EEPD: R327.1, U301.71 (EEPD)
S3_IREF: R317.1, U301.86 (IREF)
S3_JTAGL: R328.1, U301.89 (TCK), U301.92 (TMS), U301.93 (TDI), U301.94 (TRST_L)
S3_PRSNT3: R321.1, U301.21 (PRSNT3)
S3_PST0: LED32.1 (K), U301.67 (PORTSTATUS0)
S3_PST1: LED33.1 (K), U301.68 (PORTSTATUS1)
S3_PWRSAV: R322.1, U301.28 (PWR_SAV)
S3_REXT: R318.1, U301.116 (REXT)
S3_SLOTCLK: R319.1, U301.33 (SLOTCLK)
S3_SLOTIMP: R320.1, U301.45 (SLOT_IMP1), U301.46 (SLOT_IMP2)
S3_SMBCLK: R325.1, U301.26 (SMBCLK)
S3_SMBDAT: R326.1, U301.27 (SMBDATA)
S3_TEST1: R323.1, U301.9 (TEST1)
S3_TESTL: R324.1, U301.16 (TEST2), U301.17 (TEST3), U301.18 (VC1_EN), U301.22 (TEST4), U301.25 (TEST5), U301.51 (TEST6)
SCL: J_AB1.12, J_PANEL.5, R55.1, TP11.1, U1.101 (SCL_MDC), U5.3 (SCL), U6.22 (SCL), U7.22 (SCL), U8.6 (SCL), U9.8 (SCL), U10.1 (SCL), U41.92 (PB6), U51.92 (PB6), U61.92 (PB6)
SCL_CM1: J_DBG1.5, U30A.56 (GPIO3)
SCL_CM2: J_DBG2.5, U31A.56 (GPIO3)
SCL_CM3: J_DBG3.5, U32A.56 (GPIO3)
SDA: J_AB1.11, J_PANEL.4, R54.1, TP10.1, U1.98 (SDI_SDA), U5.4 (SDAI), U5.5 (SDAO), U6.23 (SDA), U7.23 (SDA), U8.5 (SDA), U9.7 (SDA), U10.6 (SDA), U41.93 (PB7), U51.93 (PB7), U61.93 (PB7)
SDA_CM1: J_DBG1.4, U30A.58 (GPIO2)
SDA_CM2: J_DBG2.4, U31A.58 (GPIO2)
SDA_CM3: J_DBG3.4, U32A.58 (GPIO2)
SEL1_A: R480.1, TP514.1, U41.22 (PA0), U70.1 (SEL1_A), U70.9 (SEL1_A)
SEL1_AB: U70.3 (SEL1_AB), U76.1 (SEL1_AB)
SEL1_B: R481.1, TP515.1, U51.22 (PA0), U70.2 (SEL1_B), U70.4 (SEL1_B)
SEL1_BC: U70.6 (SEL1_BC), U76.2 (SEL1_BC)
SEL1_C: R482.1, TP516.1, U61.22 (PA0), U70.5 (SEL1_C), U70.10 (SEL1_C)
SEL1_CA: U70.8 (SEL1_CA), U76.5 (SEL1_CA)
SEL1_O1: U76.3 (SEL1_O1), U76.4 (SEL1_O1)
SEL2_A: R483.1, TP517.1, U41.23 (PA1), U70.13 (SEL2_A), U71.5 (SEL2_A)
SEL2_AB: U70.11 (SEL2_AB), U76.10 (SEL2_AB)
SEL2_B: R484.1, TP518.1, U51.23 (PA1), U70.12 (SEL2_B), U71.1 (SEL2_B)
SEL2_BC: U71.3 (SEL2_BC), U76.9 (SEL2_BC)
SEL2_C: R485.1, TP519.1, U61.23 (PA1), U71.2 (SEL2_C), U71.4 (SEL2_C)
SEL2_CA: U71.6 (SEL2_CA), U76.12 (SEL2_CA)
SEL2_O1: U76.8 (SEL2_O1), U76.13 (SEL2_O1)
SEL3_A: R486.1, TP520.1, U41.24 (PA2), U71.10 (SEL3_A), U72.2 (SEL3_A)
SEL3_AB: U71.8 (SEL3_AB), U77.1 (SEL3_AB)
SEL3_B: R487.1, TP521.1, U51.24 (PA2), U71.9 (SEL3_B), U71.13 (SEL3_B)
SEL3_BC: U71.11 (SEL3_BC), U77.2 (SEL3_BC)
SEL3_C: R488.1, TP522.1, U61.24 (PA2), U71.12 (SEL3_C), U72.1 (SEL3_C)
SEL3_CA: U72.3 (SEL3_CA), U77.5 (SEL3_CA)
SEL3_O1: U77.3 (SEL3_O1), U77.4 (SEL3_O1)
SHORE_INHIBIT: J_AB1.21, J_PANEL.26
SIM1_CLK: J_M2C2.32 (UIM-CLK), R267.1
SIM1_IO: J_M2C2.34 (UIM-DATA), R268.1
SIM1_RST: J_M2C2.30 (UIM-RESET), R266.1
SIM1_VCC: C286.1, J_M2C2.36 (UIM-PWR), J_SIM1.1 (VCC)
SIM2_CLK: J_M2C2.44 (GPIO_2), R288.1
SIM2_IO: J_M2C2.42 (GPIO_1), R289.1
SIM2_RST: J_M2C2.46 (GPIO_3), R287.1
SIM2_VCC: J_M2C2.48 (GPIO_4), R272.1
SIMC1_CLK: C288.1, J_SIM1.3 (CLK), R267.2
SIMC1_IO: C287.1, J_SIM1.7 (I/O), R268.2
SIMC1_RST: C283.1, J_SIM1.2 (RST), R266.2
SIMC2_CLK: C291.1, J_SIM2.3 (CLK), R270.2
SIMC2_IO: C290.1, J_SIM2.7 (I/O), R271.2
SIMC2_RST: C284.1, J_SIM2.2 (RST), R269.2
SIMC2_VCC: C289.1, J_SIM2.1 (VCC), R272.2
SIMR2_CLK: R270.1, R288.2
SIMR2_IO: R271.1, R289.2
SIMR2_RST: R269.1, R287.2
SLOT_EN1: J_AB1.17, J_PANEL.21
SLOT_EN2: J_AB1.18, J_PANEL.22
SLOT_EN3: J_AB1.19, J_PANEL.23
SPI3_CE0: J_SPI3.6, U32A.39 (GPIO8)
SPI3_CE1: J_SPI3.7, R25.1, U12.19 (NSS), U32A.37 (GPIO7)
SPI3_IO23: J_SPI3.8, U12.14 (BUSY), U32A.47 (GPIO23)
SPI3_IO24: J_SPI3.9, U12.13 (DIO1), U32A.45 (GPIO24)
SPI3_IO26: J_SPI3.10, U12.15 (NRST), U32A.24 (GPIO26)
SPI3_MISO: J_SPI3.3, U12.16 (MISO), U32A.40 (GPIO9)
SPI3_MOSI: J_SPI3.4, U12.17 (MOSI), U32A.44 (GPIO10)
SPI3_SCLK: J_SPI3.5, U12.18 (SCK), U32A.38 (GPIO11)
SWA_IN: C502.2, U82.5 (SWA_IN)
SWA_O1: C500.2, U82.1 (SWA_O1)
SWA_O2: C501.2, U82.3 (SWA_O2)
SWB_IN: C505.2, U83.5 (SWB_IN)
SWB_O1: C503.2, U83.1 (SWB_O1)
SWB_O2: C504.2, U83.3 (SWB_O2)
SWP1_A_N: C176.2, U1.2 (TXRX1M_A)
SWP1_A_P: C175.2, U1.1 (TXRX1P_A)
SWP1_B_N: C178.2, U1.5 (TXRX1M_B)
SWP1_B_P: C177.2, U1.4 (TXRX1P_B)
SWP1_C_N: C180.2, U1.7 (TXRX1M_C)
SWP1_C_P: C179.2, U1.6 (TXRX1P_C)
SWP1_D_N: C182.2, U1.9 (TXRX1M_D)
SWP1_D_P: C181.2, U1.8 (TXRX1P_D)
SWP2_A_N: C276.2, U1.13 (TXRX2M_A)
SWP2_A_P: C275.2, U1.12 (TXRX2P_A)
SWP2_B_N: C278.2, U1.16 (TXRX2M_B)
SWP2_B_P: C277.2, U1.15 (TXRX2P_B)
SWP2_C_N: C280.2, U1.18 (TXRX2M_C)
SWP2_C_P: C279.2, U1.17 (TXRX2P_C)
SWP2_D_N: C282.2, U1.21 (TXRX2M_D)
SWP2_D_P: C281.2, U1.20 (TXRX2P_D)
SWP3_A_N: C376.2, U1.25 (TXRX3M_A)
SWP3_A_P: C375.2, U1.24 (TXRX3P_A)
SWP3_B_N: C378.2, U1.27 (TXRX3M_B)
SWP3_B_P: C377.2, U1.26 (TXRX3P_B)
SWP3_C_N: C380.2, U1.29 (TXRX3M_C)
SWP3_C_P: C379.2, U1.28 (TXRX3P_C)
SWP3_D_N: C382.2, U1.32 (TXRX3M_D)
SWP3_D_P: C381.2, U1.31 (TXRX3P_D)
SWP4_A_N: T1.3 (TD1N), U1.35 (TXRX4M_A)
SWP4_A_P: T1.2 (TD1P), U1.34 (TXRX4P_A)
SWP4_B_N: T1.6 (TD2N), U1.38 (TXRX4M_B)
SWP4_B_P: T1.5 (TD2P), U1.37 (TXRX4P_B)
SWP4_C_N: T1.9 (TD3N), U1.40 (TXRX4M_C)
SWP4_C_P: T1.8 (TD3P), U1.39 (TXRX4P_C)
SWP4_D_N: T1.12 (TD4N), U1.43 (TXRX4M_D)
SWP4_D_P: T1.11 (TD4P), U1.42 (TXRX4P_D)
TCT1: C29.1, T1.1 (TCT1)
TCT2: C30.1, T1.4 (TCT2)
TCT3: C31.1, T1.7 (TCT3)
TCT4: C32.1, T1.10 (TCT4)
TR_APRS: J_AB1.14, J_PANEL.7
TX_INHIBIT_n: J_AB1.16, J_PANEL.11, R59.1
U23_DVDT: C56.1, U23.2 (U23_DVDT)
U23_ILM: R36.1, U23.7 (U23_ILM)
U23_OVLO: R38.2, R39.1, U23.8 (U23_OVLO)
U24_DVDT: C61.1, U24.2 (U24_DVDT)
U24_ILM: R43.1, U24.7 (U24_ILM)
U24_OVLO: R45.2, R46.1, U24.8 (U24_OVLO)
UART0_RX1: J_DBG1.3, U30A.51 (GPIO15)
UART0_RX2: J_DBG2.3, U31A.51 (GPIO15)
UART0_RX3: J_DBG3.3, U32A.51 (GPIO15)
UART0_TX1: J_DBG1.2, U30A.55 (GPIO14)
UART0_TX2: J_DBG2.2, U31A.55 (GPIO14)
UART0_TX3: J_DBG3.2, U32A.55 (GPIO14)
USB_5G_N: J_M2C2.9 (USB_D-), U302.25 (USB_DM_DN4)
USB_5G_P: J_M2C2.7 (USB_D+), U302.24 (USB_DP_DN4)
USB_D8_N: J_AB1.2, U302.2 (USB_DM_DN1)
USB_D8_P: J_AB1.1, U302.1 (USB_DP_DN1)
USB_E6_N: J_AB1.26, U302.10 (USB_DM_DN2)
USB_E6_P: J_AB1.25, U302.9 (USB_DP_DN2)
USB_OTG_N1: J_FLASH1.A7 (D-), J_FLASH1.B7 (D-), U30B.103 (USB_N), U107.3 (I/O2), U107.4 (I/O2)
USB_OTG_N2: J_FLASH2.A7 (D-), J_FLASH2.B7 (D-), U31B.103 (USB_N), U207.3 (I/O2), U207.4 (I/O2)
USB_OTG_N3: J_FLASH3.A7 (D-), J_FLASH3.B7 (D-), U32B.103 (USB_N), U307.3 (I/O2), U307.4 (I/O2)
USB_OTG_P1: J_FLASH1.A6 (D+), J_FLASH1.B6 (D+), U30B.105 (USB_P), U107.1 (I/O1), U107.6 (I/O1)
USB_OTG_P2: J_FLASH2.A6 (D+), J_FLASH2.B6 (D+), U31B.105 (USB_P), U207.1 (I/O1), U207.6 (I/O1)
USB_OTG_P3: J_FLASH3.A6 (D+), J_FLASH3.B6 (D+), U32B.105 (USB_P), U307.1 (I/O1), U307.6 (I/O1)
USB_PNL_N: J_PANEL.16, U37.3 (I/O2), U37.4 (I/O2), U102.10 (USB_DM_DN2)
USB_PNL_P: J_PANEL.15, U37.1 (I/O1), U37.6 (I/O1), U102.9 (USB_DP_DN2)
USB_WALL_N: J_AB2.2, U29.3 (I/O2), U29.4 (I/O2), U302.18 (USB_DM_DN3)
USB_WALL_P: J_AB2.1, U29.1 (I/O1), U29.6 (I/O1), U302.17 (USB_DP_DN3)
VBAT: BT1.1 (+), TP6.1, U9.6 (VBAT), U11.22 (V_BCKP), U30A.76 (VBAT), U31A.76 (VBAT), U32A.76 (VBAT)
VBUS_FLASH1: J_FLASH1.A4 (VBUS), J_FLASH1.A9 (VBUS), J_FLASH1.B4 (VBUS), J_FLASH1.B9 (VBUS), U107.5 (VBUS)
VBUS_FLASH2: J_FLASH2.A4 (VBUS), J_FLASH2.A9 (VBUS), J_FLASH2.B4 (VBUS), J_FLASH2.B9 (VBUS), U207.5 (VBUS)
VBUS_FLASH3: J_FLASH3.A4 (VBUS), J_FLASH3.A9 (VBUS), J_FLASH3.B4 (VBUS), J_FLASH3.B9 (VBUS), U307.5 (VBUS)
VBUS_QMX: F3.2, J_QMX.1, U35.5 (VBUS)
W1A_CARD: C500.1, J_W1A.1 (In)
W1B_CARD: C503.1, J_W1B.1 (In)
W3A_CARD: C501.1, J_W3A.1 (In)
W3B_CARD: C504.1, J_W3B.1 (In)
WA_ANT: C502.1, J_WOA.1 (In)
WB_ANT: C505.1, J_WOB.1 (In)
WIFI2_W_DIS2_n: J_M2C3.54 (~W_DISABLE2), R338.1
WIFI2_W_DIS_n: J_M2C3.56 (~W_DISABLE1), Q306.3 (D), R337.1
WIFI2_nLED: J_M2C3.6 (~LED_1), LED35.1 (K)
WIFI_PRI: Q10.3 (D), R510.1, U82.6 (WIFI_PRI), U83.6 (WIFI_PRI)
WIFI_SEC: Q10.1 (G), TP510.1, U41.41 (PE11), U51.41 (PE11), U61.41 (PE11), U79.6 (WIFI_SEC), U82.4 (WIFI_SEC), U83.4 (WIFI_SEC)
WIFI_W_DIS2_n: J_M2C1.54 (~W_DISABLE2), R138.1
WIFI_W_DIS_n: J_M2C1.56 (~W_DISABLE1), Q106.3 (D), R137.1
WIFI_nLED: J_M2C1.6 (~LED_1), LED15.1 (K)
WL_nDIS1: Q109.3 (D), U30A.89 (WL_nDisable)
WL_nDIS1_KILL: Q109.1 (G), R173.1, U111.3 (WL_nDIS1_KILL)
WL_nDIS1_OFF: R162.1, U6.13 (IO1_0), U111.1 (WL_nDIS1_OFF)
WL_nDIS2: Q209.3 (D), U31A.89 (WL_nDisable)
WL_nDIS2_KILL: Q209.1 (G), R273.1, U211.3 (WL_nDIS2_KILL)
WL_nDIS2_OFF: R262.1, U6.14 (IO1_1), U211.1 (WL_nDIS2_OFF)
WL_nDIS3: Q309.3 (D), U32A.89 (WL_nDisable)
WL_nDIS3_KILL: Q309.1 (G), R373.1, U311.3 (WL_nDIS3_KILL)
WL_nDIS3_OFF: R362.1, U6.15 (IO1_2), U311.1 (WL_nDIS3_OFF)
WSEC_A: R498.1, TP532.1, U41.37 (PE7), U74.10 (WSEC_A), U75.2 (WSEC_A)
WSEC_AB: U74.8 (WSEC_AB), U79.1 (WSEC_AB)
WSEC_B: R499.1, TP533.1, U51.37 (PE7), U74.9 (WSEC_B), U74.13 (WSEC_B)
WSEC_BC: U74.11 (WSEC_BC), U79.2 (WSEC_BC)
WSEC_C: R500.1, TP534.1, U61.37 (PE7), U74.12 (WSEC_C), U75.1 (WSEC_C)
WSEC_CA: U75.3 (WSEC_CA), U79.5 (WSEC_CA)
WSEC_O1: U79.3 (WSEC_O1), U79.4 (WSEC_O1)
ZBA_3V3: C48.1, C49.1, R26.2, U16.6 (VDD)
ZBA_BSL: R30.1, U13.10 (ZBA_BSL), U16.28 (DTR)
ZBA_DM: U16.5 (D-), U202.10 (USB_DM_DN2)
ZBA_DP: U16.4 (D+), U202.9 (USB_DP_DN2)
ZBA_LED_G: R34.1, U13.3 (ZBA_LED_G)
ZBA_LED_R: R32.1, U13.2 (ZBA_LED_R)
ZBA_RST: R26.1, U16.9 (RSTb)
ZBA_RST_n: J_ZBDBG1.5, R28.1, U13.24 (ZBA_RST_n), U16.24 (RTS)
ZBA_RXD: U13.7 (ZBA_RXD), U16.26 (TXD)
ZBA_TCKC: J_ZBDBG1.4, U13.14 (ZBA_TCKC)
ZBA_TMSC: J_ZBDBG1.3, U13.13 (ZBA_TMSC)
ZBA_TXD: U13.8 (ZBA_TXD), U16.25 (RXD)
ZBB_3V3: C50.1, C51.1, R27.2, U17.6 (VDD)
ZBB_BSL: R31.1, U14.10 (ZBB_BSL), U17.28 (DTR)
ZBB_DM: U17.5 (D-), U202.18 (USB_DM_DN3)
ZBB_DP: U17.4 (D+), U202.17 (USB_DP_DN3)
ZBB_LED_G: R35.1, U14.3 (ZBB_LED_G)
ZBB_LED_R: R33.1, U14.2 (ZBB_LED_R)
ZBB_RST: R27.1, U17.9 (RSTb)
ZBB_RST_n: J_ZBDBG2.5, R29.1, U14.24 (ZBB_RST_n), U17.24 (RTS)
ZBB_RXD: U14.7 (ZBB_RXD), U17.26 (TXD)
ZBB_TCKC: J_ZBDBG2.4, U14.14 (ZBB_TCKC)
ZBB_TMSC: J_ZBDBG2.3, U14.13 (ZBB_TMSC)
ZBB_TXD: U14.8 (ZBB_TXD), U17.25 (RXD)
ZB_ON: R53.1, U6.8 (IO0_4), U20.2 (ZB_ON)
ZEROIZE_HW: J_AB1.20, J_PANEL.10, TP8.1
nRPIBOOT1: J_RPIBOOT1.1, U30A.93 (nRPIBOOT)
nRPIBOOT2: J_RPIBOOT2.1, U31A.93 (nRPIBOOT)
nRPIBOOT3: J_RPIBOOT3.1, U32A.93 (nRPIBOOT)

Notes on the sheet:
PCB-B COMPUTE B21
SHARED POWER
SHARED POWER: DEVICE RAIL, +3V3_DEV, KSZ CORE RAILS, CR2032
page 1 of 38 MeshSat field kit V2, CERN-OHL-S-2.0 PROTOTYPE, nothing built 2026-09-26
JST-VH socket
AP63203WU-7 3.3 V 2 A buck
4.7uH
TPS62933DRLR buck 1.2 V Ethernet s..
2.2uH
AP2112K-2.5 LDO
CR2032 holder Keystone 3034
p31,32,33,34,..
p32
p9,17,25,28
p26,27,32,33,..
p27
p27,32
SLOT S1
SLOT S1: COMPUTE MODULE 5, PCIe SWITCH, USB 3 HUB, M.2 SOCKETS, RAILS, SUPPORT
page 2 of 38 MeshSat field kit V2, CERN-OHL-S-2.0 PROTOTYPE, nothing built 2026-09-26
Amphenol 10164227-1004A1RLF recept..
green ACT
decoupling of U30A
SMBJ6.0A
p26
SLOT S1: COMPUTE MODULE 5, PCIe SWITCH, USB 3 HUB, M.2 SOCKETS, RAILS, SUPPORT (continued)
page 3 of 38 MeshSat field kit V2, CERN-OHL-S-2.0 PROTOTYPE, nothing built 2026-09-26
AP64500SP-13 5 A buck
68k
22u 10V
2N7002
TPS62933DRLR buck 1.0 V PCIe switc..
p6,7
page 4 of 38 MeshSat field kit V2, CERN-OHL-S-2.0 PROTOTYPE, nothing built 2026-09-26
TPS62933DRLR buck 1.1 V hub core S1
page 5 of 38 MeshSat field kit V2, CERN-OHL-S-2.0 PROTOTYPE, nothing built 2026-09-26
Diodes PI7C9X2G404SL PCIe 2.0 switch
green NVMe link
green card link
33.2R 1%
49.9R 1%
475 1%
220n 16V
100n 16V
1.43k 1%
page 6 of 38 MeshSat field kit V2, CERN-OHL-S-2.0 PROTOTYPE, nothing built 2026-09-26
decoupling of U101
M.2 M-key 2242 socket
p3,7
page 7 of 38 MeshSat field kit V2, CERN-OHL-S-2.0 PROTOTYPE, nothing built 2026-09-26
M.2 E-key 2230 socket
SN74LVC32APWR quad OR
p3,6
p3,15,16,19,..
page 8 of 38 MeshSat field kit V2, CERN-OHL-S-2.0 PROTOTYPE, nothing built 2026-09-26
TI TUSB8041IRGCR four-port USB 3.0..
TI TMUXHS4212 SuperSpeed 2:1 host..
TI TS3USB221A USB2 2:1 host select
BC857
IP68 cooler fan of S1
p30
p31
p30,32
p37
p33,34,35,37
p11
page 9 of 38 MeshSat field kit V2, CERN-OHL-S-2.0 PROTOTYPE, nothing built 2026-09-26
nRPIBOOT jumper S1
console UART0 and the module I2C o..
5mOhm 1% 2512
p17,25,32
p1,17,25,28
p32,33,34,35
SLOT S2
SLOT S2: COMPUTE MODULE 5, PCIe SWITCH, USB 3 HUB, M.2 SOCKETS, RAILS, SUPPORT
page 10 of 38 MeshSat field kit V2, CERN-OHL-S-2.0 PROTOTYPE, nothing built 2026-09-26
decoupling of U31A
p17
p16
SLOT S2: COMPUTE MODULE 5, PCIe SWITCH, USB 3 HUB, M.2 SOCKETS, RAILS, SUPPORT (continued)
page 11 of 38 MeshSat field kit V2, CERN-OHL-S-2.0 PROTOTYPE, nothing built 2026-09-26
p14,15
p13
page 12 of 38 MeshSat field kit V2, CERN-OHL-S-2.0 PROTOTYPE, nothing built 2026-09-26
TPS62933DRLR buck 1.1 V hub core S2
page 13 of 38 MeshSat field kit V2, CERN-OHL-S-2.0 PROTOTYPE, nothing built 2026-09-26
p14
p15
page 14 of 38 MeshSat field kit V2, CERN-OHL-S-2.0 PROTOTYPE, nothing built 2026-09-26
decoupling of U201
p11,15
page 15 of 38 MeshSat field kit V2, CERN-OHL-S-2.0 PROTOTYPE, nothing built 2026-09-26
M.2 B-key 3052 socket
decoupling of J_M2C2
220u 6.3V
6.8n 50V
220p 50V
68p 50V
15p 50V
9.1p 50V
4.7p 50V
2N7002 expander -> FULL_CARD_POWER..
2N7002 expander -> RESET#
p11,14
p24
p3,7,16,19,..
p31,32
page 16 of 38 MeshSat field kit V2, CERN-OHL-S-2.0 PROTOTYPE, nothing built 2026-09-26
nano-SIM push-push GCT SIM8060
10p 50V
p3,7,15,19,..
p10
p29
page 17 of 38 MeshSat field kit V2, CERN-OHL-S-2.0 PROTOTYPE, nothing built 2026-09-26
IP68 cooler fan of S2
nRPIBOOT jumper S2
p19
p9,25,32
p1,9,25,28
SLOT S3
SLOT S3: COMPUTE MODULE 5, PCIe SWITCH, USB 3 HUB, M.2 SOCKETS, RAILS, SUPPORT
page 18 of 38 MeshSat field kit V2, CERN-OHL-S-2.0 PROTOTYPE, nothing built 2026-09-26
decoupling of U32A
p25,29
p25
p23
SLOT S3: COMPUTE MODULE 5, PCIe SWITCH, USB 3 HUB, M.2 SOCKETS, RAILS, SUPPORT (continued)
page 19 of 38 MeshSat field kit V2, CERN-OHL-S-2.0 PROTOTYPE, nothing built 2026-09-26
p22,23
p21
page 20 of 38 MeshSat field kit V2, CERN-OHL-S-2.0 PROTOTYPE, nothing built 2026-09-26
TPS62933DRLR buck 1.1 V hub core S3
page 21 of 38 MeshSat field kit V2, CERN-OHL-S-2.0 PROTOTYPE, nothing built 2026-09-26
p22
page 22 of 38 MeshSat field kit V2, CERN-OHL-S-2.0 PROTOTYPE, nothing built 2026-09-26
decoupling of U301
p19,23
page 23 of 38 MeshSat field kit V2, CERN-OHL-S-2.0 PROTOTYPE, nothing built 2026-09-26
blue WiFi link
p19,22
p3,7,15,16,..
p18
page 24 of 38 MeshSat field kit V2, CERN-OHL-S-2.0 PROTOTYPE, nothing built 2026-09-26
IP68 cooler fan of S3
page 25 of 38 MeshSat field kit V2, CERN-OHL-S-2.0 PROTOTYPE, nothing built 2026-09-26
nRPIBOOT jumper S3
SPI0 breakout of S3
p18,29
p9,17,32
p1,9,17,28
SHARED
SHARED: ETHERNET SWITCH KSZ9897R: PORTS 1-3 THE MODULES, PORT 4 THE WALL RJ45 THROUGH THE..
page 26 of 38 MeshSat field kit V2, CERN-OHL-S-2.0 PROTOTYPE, nothing built 2026-09-26
Microchip KSZ9897RTXI seven-port G..
6.04k 1%
decoupling of U1
p1,27,32,33,..
SHARED | SHARED
SHARED: ETHERNET SWITCH KSZ9897R: PORTS 1-3 THE MODULES, PORT 4 THE WALL RJ45 THROUGH THE.. (continued)
SHARED: DISPLAY SWITCH: TWO TS3DV642 IN CASCADE TO THE HDMI RECEPTACLE; SEL2 CHOOSES THE SLOT..
page 27 of 38 MeshSat field kit V2, CERN-OHL-S-2.0 PROTOTYPE, nothing built 2026-09-26
Pulse H5007NL 1000BASE-T magnetics
0R 2512
RJ45 jack
TI TPS23861PWR PoE PSE controller
0.25R 1%
CSD19532Q5B 100 V N-FET
TI TS3DV642A0RUAR HDMI 2:1 switch
p1,26,32,33,..
p26,32
p1,32
p28
SHARED: DISPLAY SWITCH: TWO TS3DV642 IN CASCADE TO THE HDMI RECEPTACLE; SEL2 CHOOSES THE SLOT.. (continued)
SHARED: GNSS LG290P ON A CP2102N BRIDGE (BANK 2 HUB, PORT 1; A BANK IS NOT A SLOT SINCE THE I/O..
page 28 of 38 MeshSat field kit V2, CERN-OHL-S-2.0 PROTOTYPE, nothing built 2026-09-26
HDMI type A receptacle
Quectel LG290P03AAMD GNSS RTK module
decoupling of U11
U.FL socket
27nH 0402
LG290P UART2
p1,9,17,25
SHARED | SHARED | SHARED
SHARED: GNSS LG290P ON A CP2102N BRIDGE (BANK 2 HUB, PORT 1; A BANK IS NOT A SLOT SINCE THE I/O.. (continued)
SHARED: LORA E22-900M30S ON S3'S SPI0, 5 V THROUGH A TPS22810 GATED BY EMCON; ANTENNA PAD TO A..
SHARED: TWO E72 CC2652P RADIOS (ZIGBEE COORDINATOR, THREAD RCP) ON CP2102N BRIDGES (BANK 2 HUB,..
page 29 of 38 MeshSat field kit V2, CERN-OHL-S-2.0 PROTOTYPE, nothing built 2026-09-26
CP2102N-A02-GQFN28 USB-UART bridge
Ebyte E22-900M30S 1 W LoRa
Ebyte E72-2G4M20S1E CC2652P
red ZBA
green ZBA
CC2652P cJTAG ZBA
p18,25
SHARED: TWO E72 CC2652P RADIOS (ZIGBEE COORDINATOR, THREAD RCP) ON CP2102N BRIDGES (BANK 2 HUB,.. (continued)
SHARED: LIMESDR MINI RECEPTACLE (BANK 1 HUB, PORT 1, USB 3) AND THE ROCKBLOCK 9704 HEADER (BANK..
page 30 of 38 MeshSat field kit V2, CERN-OHL-S-2.0 PROTOTYPE, nothing built 2026-09-26
red ZBB
green ZBB
CC2652P cJTAG ZBB
