meshsat/meshsat-fieldkit/v2/docs/records/r8int6/evidence-phase/audit-diff.txt

A: 13 row(s) moved; layout entry not ready reasons 7 -> not ready reasons 18
  BAT-002  PASS CURRENT_CANDIDATE (BOUND) -> PASS AWAITING_REVALIDATION (OTHER_DESIGN)
  CMP-001  PASS VALID_HISTORICAL (RATIONALE) -> PASS AWAITING_REVALIDATION (NETLIST_MISMATCH)
  INT-001  PASS CURRENT_CANDIDATE (BOUND) -> PASS AWAITING_REVALIDATION (NETLIST_MISMATCH)
  PWR-001  PASS VALID_HISTORICAL (RATIONALE) -> PASS AWAITING_REVALIDATION (NETLIST_MISMATCH)
  PWR-002  PASS CURRENT_CANDIDATE (BOUND) -> PASS AWAITING_REVALIDATION (NETLIST_MISMATCH)
  PWR-003  PASS CURRENT_CANDIDATE (BOUND) -> PASS AWAITING_REVALIDATION (NETLIST_MISMATCH)
  RF-002   FAIL CURRENT_CANDIDATE (BOUND) -> FAIL AWAITING_REVALIDATION (TOOL_CHANGED)
  SCH-001  PASS CURRENT_CANDIDATE (BOUND) -> PASS AWAITING_REVALIDATION (NETLIST_MISMATCH)
  SCH-003  PASS AWAITING_REVALIDATION (UNBOUND) -> PASS AWAITING_REVALIDATION (TOOL_CHANGED)
  SCH-004  PASS CURRENT_CANDIDATE (BOUND) -> PASS AWAITING_REVALIDATION (NETLIST_MISMATCH)
  SCH-005  PASS CURRENT_CANDIDATE (BOUND) -> PASS AWAITING_REVALIDATION (NETLIST_MISMATCH)
  SI-001   INCONCLUSIVE VALID_HISTORICAL (RATIONALE) -> INCONCLUSIVE AWAITING_REVALIDATION (NETLIST_MISMATCH)
  TRN-001  PASS CURRENT_CANDIDATE (BOUND) -> PASS AWAITING_REVALIDATION (NETLIST_MISMATCH)
B: 13 row(s) moved; layout entry not ready reasons 7 -> not ready reasons 17
  CLK-001  PASS CURRENT_CANDIDATE (BOUND) -> PASS AWAITING_REVALIDATION (NETLIST_MISMATCH)
  CMP-001  PASS VALID_HISTORICAL (RATIONALE) -> PASS AWAITING_REVALIDATION (NETLIST_MISMATCH)
  INT-001  PASS CURRENT_CANDIDATE (BOUND) -> PASS AWAITING_REVALIDATION (NETLIST_MISMATCH)
  PWR-001  PASS VALID_HISTORICAL (RATIONALE) -> PASS AWAITING_REVALIDATION (NETLIST_MISMATCH)
  PWR-002  PASS CURRENT_CANDIDATE (BOUND) -> PASS AWAITING_REVALIDATION (NETLIST_MISMATCH)
  PWR-003  PASS CURRENT_CANDIDATE (BOUND) -> PASS AWAITING_REVALIDATION (NETLIST_MISMATCH)
  RF-002   FAIL CURRENT_CANDIDATE (BOUND) -> FAIL AWAITING_REVALIDATION (TOOL_CHANGED)
  SCH-001  PASS CURRENT_CANDIDATE (BOUND) -> PASS AWAITING_REVALIDATION (NETLIST_MISMATCH)
  SCH-003  INCONCLUSIVE AWAITING_REVALIDATION (UNBOUND) -> INCONCLUSIVE AWAITING_REVALIDATION (TOOL_CHANGED)
  SCH-004  PASS CURRENT_CANDIDATE (BOUND) -> PASS AWAITING_REVALIDATION (NETLIST_MISMATCH)
  SCH-005  PASS CURRENT_CANDIDATE (BOUND) -> PASS AWAITING_REVALIDATION (NETLIST_MISMATCH)
  SI-001   INCONCLUSIVE VALID_HISTORICAL (RATIONALE) -> INCONCLUSIVE AWAITING_REVALIDATION (NETLIST_MISMATCH)
  TRN-001  PASS CURRENT_CANDIDATE (BOUND) -> PASS AWAITING_REVALIDATION (NETLIST_MISMATCH)
C: 10 row(s) moved; layout entry not ready reasons 5 -> not ready reasons 11
  CLK-001  PASS CURRENT_CANDIDATE (BOUND) -> PASS AWAITING_REVALIDATION (NETLIST_MISMATCH)
  CMP-001  PASS VALID_HISTORICAL (RATIONALE) -> PASS AWAITING_REVALIDATION (NETLIST_MISMATCH)
  INT-001  PASS CURRENT_CANDIDATE (BOUND) -> PASS AWAITING_REVALIDATION (NETLIST_MISMATCH)
  PWR-001  FAIL VALID_HISTORICAL (RATIONALE) -> FAIL AWAITING_REVALIDATION (NETLIST_MISMATCH)
  RF-002   FAIL CURRENT_CANDIDATE (BOUND) -> FAIL AWAITING_REVALIDATION (TOOL_CHANGED)
  SCH-001  PASS CURRENT_CANDIDATE (BOUND) -> PASS AWAITING_REVALIDATION (NETLIST_MISMATCH)
  SCH-003  PASS AWAITING_REVALIDATION (UNBOUND) -> PASS AWAITING_REVALIDATION (TOOL_CHANGED)
  SCH-005  PASS CURRENT_CANDIDATE (BOUND) -> PASS AWAITING_REVALIDATION (NETLIST_MISMATCH)
  SI-001   INCONCLUSIVE VALID_HISTORICAL (RATIONALE) -> INCONCLUSIVE AWAITING_REVALIDATION (NETLIST_MISMATCH)
  TRN-001  PASS CURRENT_CANDIDATE (BOUND) -> PASS AWAITING_REVALIDATION (NETLIST_MISMATCH)
D: 11 row(s) moved; layout entry not ready reasons 8 -> not ready reasons 16
  CLK-001  PASS CURRENT_CANDIDATE (BOUND) -> PASS AWAITING_REVALIDATION (NETLIST_MISMATCH)
  CMP-001  PASS VALID_HISTORICAL (RATIONALE) -> PASS AWAITING_REVALIDATION (NETLIST_MISMATCH)
  INT-001  PASS CURRENT_CANDIDATE (BOUND) -> PASS AWAITING_REVALIDATION (NETLIST_MISMATCH)
  PWR-001  INCONCLUSIVE VALID_HISTORICAL (RATIONALE) -> INCONCLUSIVE AWAITING_REVALIDATION (NETLIST_MISMATCH)
  RF-002   FAIL CURRENT_CANDIDATE (BOUND) -> FAIL AWAITING_REVALIDATION (TOOL_CHANGED)
  SCH-001  PASS CURRENT_CANDIDATE (BOUND) -> PASS AWAITING_REVALIDATION (NETLIST_MISMATCH)
  SCH-003  PASS AWAITING_REVALIDATION (UNBOUND) -> PASS AWAITING_REVALIDATION (TOOL_CHANGED)
  SCH-004  PASS CURRENT_CANDIDATE (BOUND) -> PASS AWAITING_REVALIDATION (NETLIST_MISMATCH)
  SCH-005  PASS CURRENT_CANDIDATE (BOUND) -> PASS AWAITING_REVALIDATION (NETLIST_MISMATCH)
  SI-001   INCONCLUSIVE VALID_HISTORICAL (RATIONALE) -> INCONCLUSIVE AWAITING_REVALIDATION (NETLIST_MISMATCH)
  TRN-001  PASS CURRENT_CANDIDATE (BOUND) -> PASS AWAITING_REVALIDATION (NETLIST_MISMATCH)
E: 14 row(s) moved; layout entry not ready reasons 5 -> not ready reasons 17
  BAT-002  PASS CURRENT_CANDIDATE (BOUND) -> PASS AWAITING_REVALIDATION (OTHER_DESIGN)
  CLK-001  PASS CURRENT_CANDIDATE (BOUND) -> PASS AWAITING_REVALIDATION (NETLIST_MISMATCH)
  CMP-001  PASS VALID_HISTORICAL (RATIONALE) -> PASS AWAITING_REVALIDATION (NETLIST_MISMATCH)
  INT-001  PASS CURRENT_CANDIDATE (BOUND) -> PASS AWAITING_REVALIDATION (NETLIST_MISMATCH)
  PWR-001  INCONCLUSIVE VALID_HISTORICAL (RATIONALE) -> INCONCLUSIVE AWAITING_REVALIDATION (NETLIST_MISMATCH)
  PWR-002  PASS CURRENT_CANDIDATE (BOUND) -> PASS AWAITING_REVALIDATION (NETLIST_MISMATCH)
  PWR-003  PASS CURRENT_CANDIDATE (BOUND) -> PASS AWAITING_REVALIDATION (NETLIST_MISMATCH)
  RF-002   PASS CURRENT_CANDIDATE (BOUND) -> PASS AWAITING_REVALIDATION (TOOL_CHANGED)
  SCH-001  PASS CURRENT_CANDIDATE (BOUND) -> PASS AWAITING_REVALIDATION (NETLIST_MISMATCH)
  SCH-003  PASS AWAITING_REVALIDATION (UNBOUND) -> PASS AWAITING_REVALIDATION (TOOL_CHANGED)
  SCH-004  PASS CURRENT_CANDIDATE (BOUND) -> PASS AWAITING_REVALIDATION (NETLIST_MISMATCH)
  SCH-005  PASS CURRENT_CANDIDATE (BOUND) -> PASS AWAITING_REVALIDATION (NETLIST_MISMATCH)
  SI-001   INCONCLUSIVE VALID_HISTORICAL (RATIONALE) -> INCONCLUSIVE AWAITING_REVALIDATION (NETLIST_MISMATCH)
  TRN-001  PASS CURRENT_CANDIDATE (BOUND) -> PASS AWAITING_REVALIDATION (NETLIST_MISMATCH)
E5: 2 row(s) moved; layout entry not ready reasons 2 -> not ready reasons 3
  BAT-002  PASS CURRENT_CANDIDATE (BOUND) -> PASS AWAITING_REVALIDATION (OTHER_DESIGN)
  INT-001  PASS AWAITING_REVALIDATION (UNBOUND) -> INCONCLUSIVE AWAITING_REVALIDATION (CONFIG_CHANGED)
P: 12 row(s) moved; layout entry not ready reasons 6 -> not ready reasons 14
  BAT-001  FAIL CURRENT_CANDIDATE (BOUND) -> FAIL AWAITING_REVALIDATION (CONFIG_CHANGED)
  BAT-002  PASS CURRENT_CANDIDATE (BOUND) -> PASS AWAITING_REVALIDATION (OTHER_DESIGN)
  CMP-001  PASS VALID_HISTORICAL (RATIONALE) -> PASS AWAITING_REVALIDATION (NETLIST_MISMATCH)
  INT-001  PASS CURRENT_CANDIDATE (BOUND) -> PASS AWAITING_REVALIDATION (CONFIG_CHANGED)
  PWR-001  FAIL VALID_HISTORICAL (RATIONALE) -> FAIL AWAITING_REVALIDATION (CONFIG_CHANGED)
  PWR-002  PASS CURRENT_CANDIDATE (BOUND) -> PASS AWAITING_REVALIDATION (CONFIG_CHANGED)
  RF-002   PASS CURRENT_CANDIDATE (BOUND) -> PASS AWAITING_REVALIDATION (TOOL_CHANGED)
  SCH-003  PASS AWAITING_REVALIDATION (UNBOUND) -> PASS AWAITING_REVALIDATION (TOOL_CHANGED)
  SCH-004  PASS CURRENT_CANDIDATE (BOUND) -> PASS AWAITING_REVALIDATION (CONFIG_CHANGED)
  SCH-005  PASS CURRENT_CANDIDATE (BOUND) -> PASS AWAITING_REVALIDATION (NETLIST_MISMATCH)
  SI-001   INCONCLUSIVE VALID_HISTORICAL (RATIONALE) -> INCONCLUSIVE AWAITING_REVALIDATION (CONFIG_CHANGED)
  TRN-001  PASS CURRENT_CANDIDATE (BOUND) -> PASS AWAITING_REVALIDATION (CONFIG_CHANGED)
total rows moved: 75
