meshsat/meshsat-fieldkit/v2/docs/records/int14/apply_rebind_after_circuit_set13.py

#!/usr/bin/env python3
"""Records bound to a board's committed netlist by sha, after a CIRCUIT change (MESHSAT-1357, integration set 13: stream
csi's four 27R series resistors on board C; a copy of records/int13/apply_rebind_after_circuit.py with its text for set 13).
Unlike a re-export, the new netlist differs in content, so identity cannot be proved. This script parses main's netlist and the
tree's (tx_inhibit.parse_netlist: components with value and footprint, nets with their nodes) and computes what changed: the
parts added, removed or changed (value or footprint), and the nets whose node set changed. For every record bound to the old
netlist it collects the identifiers its statement and evidence name (part references and net names as whole words) and:
  * if none of them is a changed part or net, the record's reading rests on circuitry this change did not touch: it is rebound
    with one evidence entry naming the diff it was read against;
  * otherwise the record is NOT rebound here: it is listed with the changed identifiers it names, and must be re-read by hand
    (a JUDGED map passed on the command line as RID=reason pairs rebinds it with that reason written into the entry).
Usage (repository root): python3 <this file> <board letter> <netlist path> [RID="reason" ...]. Refuses a second run."""
import hashlib, os, re, subprocess, sys

import yaml

sys.dont_write_bytecode = True
HERE = os.path.dirname(os.path.abspath(__file__))
TOP = subprocess.run(["git", "rev-parse", "--show-toplevel"], cwd=HERE, capture_output=True, check=True).stdout.decode().strip()
sys.path.insert(0, os.path.join(TOP, "v2/docs/records/int7"))  # set 13 copy of records/int13/apply_rebind_after_circuit.py
sys.path.insert(0, os.path.join(TOP, "v2/ecad/tools"))
import apply_check1_answers as A
import tx_inhibit as TX
REG = os.path.join(TOP, "v2/ecad/tools/pcb_requirements.yaml")
# The change's name in each entry (the set 12 check's m2: board A's entries named d4emcon's); the default is the text it ran with.
CHANGE = os.environ.get("REBIND_CHANGE", "the circuit change of stream csi's CSI-D3 (four 27R series resistors on board C's e-paper lines)")
WORD = re.compile(r"[A-Za-z0-9_+./-]+")


def refuse(m):
    print("apply_rebind_after_circuit_set13: REFUSED: %s" % m)
    sys.exit(2)


def sha16(b): return hashlib.sha256(b).hexdigest()[:16]


def main():
    if len(sys.argv) < 3: refuse("usage: <letter> <netlist path> [RID=reason ...]")
    letter, rel = sys.argv[1], sys.argv[2]
    judged = dict(a.split("=", 1) for a in sys.argv[3:])
    old_b = subprocess.run(["git", "-C", TOP, "show", "main:" + rel], capture_output=True, check=True).stdout
    new_b = open(os.path.join(TOP, rel), "rb").read()
    o16, n16 = sha16(old_b), sha16(new_b)
    if o16 == n16: refuse("the netlist is main's: nothing to rebind")
    tmp = os.path.join(TOP, ".rebind-old.net")
    open(tmp, "wb").write(old_b)
    try:
        old, new = TX.parse_netlist(tmp), TX.parse_netlist(os.path.join(TOP, rel))
    finally:
        os.remove(tmp)
    oc, nc = old["comps"], new["comps"]
    parts = sorted(set(oc) ^ set(nc)) + sorted(r for r in set(oc) & set(nc) if (oc[r]["value"], oc[r].get("fp")) != (nc[r]["value"], nc[r].get("fp")))
    on, nn = old["nets"], new["nets"]
    def nodes(d, k): return sorted((r, p) for r, p, *_ in d.get(k, []))
    nets = sorted(k for k in set(on) | set(nn) if nodes(on, k) != nodes(nn, k))
    changed = set(parts) | set(nets) | {n.lstrip("/") for n in nets}
    print("changed parts: %s" % parts)
    print("changed nets: %s" % nets)
    reg = open(REG, encoding="utf-8").read()
    if "apply_rebind_after_circuit_set13 %s %s" % (letter, n16) in reg: refuse("already applied")
    before = yaml.safe_load(reg)
    import re as _re
    # set 13: the older binding is read from the parsed evidence_bound_to fields only (an evidence sentence may quote an
    # older sha, as board C's set 6 netlist 3fddbb3e is quoted in CON-010's text)
    shas = sorted({b.split("@", 1)[1] for r in before["records"] for b in (r.get("evidence_bound_to") or [])
                   if b.startswith(rel + "@")} - {n16})
    if len(shas) != 1: refuse("records carry %d distinct older bindings of %s: %s" % (len(shas), rel, shas))
    key = "%s@%s" % (rel, shas[0])   # the binding to move (main's, or an earlier set 12 export); every change is computed against main
    bound = [r for r in before["records"] if key in (r.get("evidence_bound_to") or [])]
    out, done, manual = reg, [], []
    for r in bound:
        text = " ".join(str(x) for x in (r.get("evidence") or [])) + " " + str(r.get("statement", "")) + " " + str(r.get("acceptance", ""))
        hit = sorted(changed & set(WORD.findall(text)))
        if hit and r["id"] not in judged:
            manual.append((r["id"], hit)); continue
        why = judged.get(r["id"]) or "none of the parts or nets this record names changed"
        entry = ("%s re-read at integration set 13 (apply_rebind_after_circuit_set13 %s %s): %s was "
                 "compared with main's netlist %s by parsed components and net node sets; changed parts %s; changed nets %s. %s; "
                 "rebound to %s. No result changes." % (rel, letter, n16, CHANGE, o16, ", ".join(parts) or "none", ", ".join(nets) or "none",
                                                      why[0].upper() + why[1:], n16))
        A.screen(entry, r["id"])
        i, j = A.span(out, r["id"])
        t = out[i:j]
        m = re.search(r"(?m)^    evidence:\n", t)
        tail = t[m.end():]
        k = re.search(r"(?m)^    [a-z_]+:", tail)
        end = m.end() + (k.start() if k else len(tail))
        t = t[:end] + "      - >-\n" + A.fold(entry, 10, 120) + t[end:]
        t = t.replace(key, "%s@%s" % (rel, n16), 1)
        out = out[:i] + t + out[j:]
        done.append(r["id"])
    if manual:
        for rid, hit in manual: print("READ BY HAND: %s names changed %s" % (rid, hit))
        refuse("%d record(s) name changed parts or nets; pass RID=reason for each after reading it" % len(manual))
    after = yaml.safe_load(out)
    rb = {r["id"]: r for r in after["records"]}
    for r in before["records"]:
        d = {f for f in set(r) | set(rb[r["id"]]) if r.get(f) != rb[r["id"]].get(f)}
        if (r["id"] in done and d != {"evidence", "evidence_bound_to"}) or (r["id"] not in done and d): refuse("%s: %s" % (r["id"], d))
    open(REG, "w", encoding="utf-8").write(out)
    if yaml.safe_load(open(REG, encoding="utf-8").read()) != after: refuse("re-parse differs")
    print("apply_rebind_after_circuit_set13: %d record(s) rebound from %s to %s: %s" % (len(done), o16, n16, ", ".join(done)))
    return 0


if __name__ == "__main__":
    sys.exit(main())
